vectivolt/PCM/docs/reference-designs/ti/tmdscncd28388d/README.md

# TMDSCNCD28388D - F28388D controlCARD (TI)
180-pin HSEC8 edge-card controlCARD carrying the TMS320F28388D: the controller our CTRL-C2000 board is built around (D-004).
- **Facts** (SPRUIL8B, May 2020; PCB rev B as of 29 May 2020): 180-pin HSEC8 connector (100-pin DIMM only via the separate TMDSADAP180TO100 adapter); default 25 MHz clock (cards MCU063B and later need C2000Ware >= 3.02, older cards use 20 MHz); on-board isolated XDS100v2 JTAG; micro-USB J3 is NOT isolated from board ground; SCI boot uses GPIO28/29.
- **Informs:** CTRL-C2000 connector/pin plan, clocking, boot and emulation arrangement (ECO-01/02).
- **Limitation:** evaluation card ("not intended to be a complete customer design"); compliance is the system designer's job. No other design in this library targets F28388D (they use F280039/F280039C, F28379D, F2803x), so reference firmware must be ported.
- **Missing (MANUAL):** schematic, BOM, layout, Gerbers and the pin-map PDFs. TI's tool page says "Hardware files can be found by downloading C2000Ware at boards\controlCARDs\TMDSCNCD28388D"; there is no separate hardware download. C2000Ware 26.02.00.00.LTS is offered only as installers (Windows .exe, Linux .run, macOS .app.zip, about 323-327 MB) from dr-download.ti.com/secure/, shown with a lock icon (TI login). Checked 2026-10-04; per the brief nothing was downloaded or run. By hand: install C2000Ware and copy the PDFs/BOM out of that folder into this directory, then add rows to SOURCES.csv.
