vectivolt/PCM/docs/requirements/ARCHITECTURE-COSTFIRST.md

# Cost-first architecture — PV-P75 / PV-P100/110 (specification for the board designers)

**Date:** 2026-10-04 · **Decision basis:** D-044, `COST-REVIEW.md` · **Scope:** REQUIREMENTS.md §2, §2b, §7 (SRC-1…5)
· **Costed parts list:** `gen/data/costfirst_bom.csv` (block level, generated by a scratch script; totals in §14)

**Honesty boundary.** Nothing here is built, bought or measured. Every number is *calculated* (from the frozen
designs in `sim/out/…`), *looked up* (a price row in `gen/data/prices.csv` or a data sheet in `docs/datasheets/`), or an
*estimate* whose basis is written next to it. Standard values (IEC 60664-1, IEC 62477-1, IEC 62109, CISPR 11) are the
transcriptions from memory already used in `sim/insulation.py` (D-032) and are **not verified against the standard
text**. 86 % of the money in §14 is a low-confidence estimate.

---

## 0. The architecture in one page

```
                    reinforced barrier B1 (the only one)
   PE-referenced / SELV  ║   DC side ("live"), everything referenced to BUS-
  ───────────────────────╫──────────────────────────────────────────────────────────────────────
   CAN (BMS/PCS)  ◄──────╫── CA-IS3062W ──┐
   RS-485         ◄──────╫── CA-IS3082W ──┤
   ENABLE / E-stop ──────╫── CA-IS3821L ──┼── F280039C (C2000, live) ── trip LATCH ── PWM gating ──► 12/16 NSI6651 channels
   STATUS out     ◄──────╫── CA-IS3821L ──┤        │  ADC / CMPSS              ▲          (functional insulation,
   3 fans (24 V)  ◄──────╫── fan buck  ◄──┤        │                           │           per-phase bias transformer)
   SELV 24 V      ◄──────╫── AUX-T1 SELV winding (reinforced)                  │
                         ║   AUX-T1 live winding 24 V ─► coils, 5 V, 3.3 V     │ OC / OV / OT / DESAT / RDY / WD / STOP
                         ║   flyback primary ◄── diode-OR of A+ and B+ terminal sides (starts at 200-220 V)
  ───────────────────────╫──────────────────────────────────────────────────────────────────────
                    basic barrier B2: DC side ↔ earthed heatsink / chassis / PE
```

- **Power stage unchanged:** 3 (4) interleaved two-level FSBB phases, 2 × SG2M040170HJ per switch, 32 kHz, NSI6651
  channel rev 6, inductor rev M1, control and MPPT as designed.
- **Controller on BUS-:** one F280039C (4.40 USD) on a small control board; dividers, shunts and TMR sensors without
  isolated amplifiers; **one reinforced barrier** (communication, enable/stop, status, fans, SELV supply).
- **Self-powered:** one 75 W flyback (AUX-HV topology) from both ports' terminal sides, starting at 200-220 V; a
  reinforced SELV winding feeds fans and communication; no cabinet 24 V.
- **Ports:** PV port = varistor network + **one contactor** (+ pole), no fuse, no precharge. Battery port = varistor
  network + **one aR fuse per pole** + one contactor + precharge relay/resistor. No clamp banks.
- **One hardware latch** (no dual channel) with OC, OV, OT, DESAT, gate-supply loss, watchdog and external stop.
- **Two boards:** power board (~1,615 parts) + control board (~236 parts) = **~1,850 parts** (PV-P75).
- **BOM at catalogue / 1 k prices: 966 USD (12.9 USD/kW)** for PV-P75, **1,177 USD** for PV-P100/110 — 65 % below
  today's 2,789 USD, but **21 % above the 800 USD budget**. Chinese-volume view (stated factors, §14): ~736 USD.
- **What closes the gap:** the frozen inductor (240 USD = 25 % of the BOM at an 80 USD estimate each) has to be
  re-opened for cost; nothing else of that size is left that does not cost safety (§14).

---

## 1. Block diagram and circuits with their reference potential

### 1.1 Power path

```
 PV array                                                                                Battery / DC bus
 A+_T ─┬─[K_A HFE82V]──── A+ ── A bank 3(4)×2×45 µF ──┐                ┌── B bank ── B+ ─[K_B HFE82V]─┬─[F_B+ 250 A aR]─┬─ B+_T
       │                                           ┌───┴───┐        ┌───┴───┐          └[K_PRE+220 Ω]─┘                 │
   varistor Y                                      │ leg A │──L1─── │ leg B │   (× 3 or 4 phases, 120°/90°)          varistor Y
   VAX, IMD, AUX tap                               └───┬───┘        └───┬───┘                                AUX tap, VBX
 A-_T ─┴──[RS_A 100 µΩ]────────────────────────── BUS- ─────────────────┴──────────[RS_B 100 µΩ]──[F_B- 250 A aR]─┴─ B-_T
                                 (BUS- = controller ground; heatsink, chassis, Y caps, MOV3, IMD → PE)
```

### 1.2 Circuits and reference potential

| circuit | board | reference | insulation to BUS- | insulation to PE | insulation to SELV |
|---|---|---|---|---|---|
| port banks, legs, dampers, bleeders, inductors | power | A+/B+/BUS-/switch nodes | functional | basic (B2) | reinforced (B1) |
| 12 (16) gate-drive islands (NSI6651 output side, bias secondary, clamps, booster, DESAT) | power | each device's Kelvin source (S1/S3: switch node; S2/S4: BUS-) | functional (driver, bias transformer) | basic (by distance on the board, B2) | reinforced |
| gate-bias primaries (SN6505B, 5 V), NSI6651 input side | power | BUS- | — | basic | reinforced |
| TMR inductor-current sensors (primary at the switch node, output at BUS-) | power | BUS- | functional (sensor) | — | reinforced |
| port dividers VA, VAX, VB, VBX; PE divider; IMD strings | power | BUS- (bottom), poles/PE (top) | functional (pole-pole) / basic (PE strings) | basic | reinforced |
| port shunts RS_A, RS_B + amplifier | power | BUS- | — (same node) | basic | reinforced |
| contactor and precharge-relay coils + drivers | power + chassis | BUS- (coil low side) | functional coil-contact (Hongfa 3 kV AC) | **basic coil-to-mounting** (open item R-04) | reinforced |
| aux flyback primary, live 24 V / 5 V / 3.3 V rails | power | BUS- | functional | basic | reinforced (AUX-T1) |
| MCU, ADC front end, comparators, latch, watchdog, debug header | control (live zone) | BUS- | — | basic (by distance, coated) | reinforced (B1) |
| CAN, RS-485, enable/stop input, status output, fan supply + PWM + tach, SELV 24 V / 5 V | control (SELV zone) + fans | SELV 0 V, tied to PE via 1 MΩ ‖ 4.7 nF (Y2); installer may bond it solid (PELV) | reinforced (B1) | — (SELV/PELV) | — |
| heatsink, chassis, fan frames' mounting, terminal covers | mechanics | PE | basic (B2) | — | — |

---

## 2. Insulation concept

Requirements are the rows of `sim/out/insulation/insulation_spec.json` (working voltage 1000 V DC, 1100 V at the OV
trip, switch-node recurring peak 1,273 V at 1000 V / 1,401 V at the trip, OVC II, PD2 inside the coated electronics
compartment, PD3 in the cooling-air path). The varistor network of `gen/port.py` rev 6 limits the terminals to
**Up,eff = 3.79 kV** pole-PE and pole-pole; where this credit is used it is marked "credit" (D-032: the credit is not
verified against the standard text).

### 2.1 The barriers that remain

| # | barrier | type | requirement (insulation_spec row) | part(s) that provide it |
|---|---|---|---|---|
| B1 | DC side ↔ SELV (communication, enable/stop, status, fans, SELV supply) | **reinforced** | "Reinforced HV-PELV, DC pole": 1000 V DC working (BUS- is a DC node; no switching swing across B1); impulse 8 kV (6 kV with credit); AC test 4400 V rms 60 s; creepage 10.0 mm PD2 on the PCB (6.4 mm under an IEC 60664-3 coating = PD1); clearance 8.0 / 9.2 / 10.4 mm at 2000 / 3000 / 4000 m (5.5 / 6.3 / 7.1 mm with credit) | AUX-T1 SELV winding (TIW-litz, potted, PD ≤ 10 pC at 2461 Vpk, 4400 V rms, 8 kV — the AUX-HV T1 rev M1 construction rules); CA-IS3062W (CAN), CA-IS3082W (RS-485), 3 × CA-IS3821L (2-ch digital isolators: enable/stop, status, fan speed, 3 tachs) — SOIC-16 WB, 8 mm package creepage → **conformal coating to PD1 over the B1 zone is mandatory** (as PA-08 required for the old isolators) or the 15 mm WW variants; a routed slot under every isolator; the SELV harness (fan leads UL1007 300 V) runs in its own channel ≥ 10 mm from live parts or in a sleeve (supplementary insulation) |
| B2 | DC side ↔ PE (heatsink, chassis, enclosure) | **basic** | "Basic HV-PE": DC pole: impulse 6 kV (4 kV credit), 2200 V rms, creepage 5.0 mm PD2 / 12.5 mm (group I) – 16 mm (IIIa) PD3, clearance 5.5 / 6.3 / 7.1 mm (3.0 / 3.5 / 3.9 mm credit); switch node additionally PD-free: extinction ≥ 1528 Vpk ≤ 10 pC at 1910 Vpk | AlN 1.0 mm device insulators with 6.5 mm overhang (cell_spec `heatsink_insulator`, unchanged); inductor winding-core-mounting (rev M1 insulation system); contactor and fuse bodies (maker ratings); terminal feed-throughs (PD3 creepage); Y1 capacitors (8 kV); MOV3 of each varistor Y; IMD strings (8 × 1210, 1000 V each); heatsink NTC probes (≥ 2.2 kV rms lead-to-lug, R-10); insulating PCB standoffs; **contactor coil-to-mounting** (new: the coil is live now — Hongfa states coil-contact 3 kV AC only, R-04) |
| B3 | inside the DC side | functional | withstand 1000 V DC + 1,401 V recurring peak + 3.79 kV pole-pole surge; **our rule:** PD-free at ≥ 1.75 kVpk (1.25 × the recurring peak) for everything that sees a switch node | NSI6651 (reinforced part, VIORM 2121 Vpk, used functionally), per-phase bias transformer (custom, §4), TMR sensors, dividers, contactor coil-contact (3 kV AC), CA-IS3417WT (IMD), CNY65B (varistor monitor), AUX-T1 primary ↔ live winding |

**What disappears:** the 132 audited HV-PELV barriers of the old platform (12 UCC14241, 12 NSI6651 as safety
barriers, AMC3330/AMC3302, TPSI3050, contactor coils, CNY65B, AUX-HV T1, LA 150-P …) become functional; the 22
barrier failures at 2000 m that came from HV-PELV parts (IC-02/03 surge ratings of AMC3302 / UCC12050, IC-04 precharge
relay, IC-05 contactor coil) no longer apply; the B2 items among them (heatsink pads, magnetics insulation, X-capacitor
specs) stay open as before. Six parts carry the safety barrier B1 (AUX-T1 and five isolators).

### 2.2 The hard questions

- **Fans.** They cannot be live: the fan's own dielectric rating is **500 V AC 1 min frame to + lead** and the leads
  are UL1007 300 V (Delta AFB1224SHE-F00 spec p.2, `docs/datasheets/thermal/AFB1224SHE-F00.pdf`), against 2200 V rms
  needed for basic insulation of a 1000 V DC circuit. The fans are therefore on the SELV side: powered from the
  reinforced SELV winding of AUX-T1 through a 7-24 V fan buck on the control board, speed command and tachs across
  B1 (isolator channels). Fan frames are plastic (UL94V-0) and mounted on the earthed chassis; the fan's internal
  insulation is only functional, which is acceptable for an SELV circuit.
- **Communication ports.** CAN and RS-485 transceivers are isolated (reinforced, B1); their bus sides, the
  terminations, TVS (SM712-class to SELV 0 V, SMBJ to PE) and the connectors sit in the SELV zone at the front panel.
  The BMS / PCS side may earth its 0 V; the SELV 0 V is tied to PE through 1 MΩ ‖ 4.7 nF Y2 so a solid bond by the
  installer (PELV) is harmless.
- **Enable / emergency-stop input.** A dry contact (or 24 V SELV signal) in the SELV zone drives a reverse isolator
  channel of the **default-low** variant: SELV supply lost, wire broken or contact open = STOP. The isolator output
  sets the hardware latch (§6) directly — firmware is not in the path. It is a single-channel functional stop, not a
  SIL/PL-rated safety function (§12).
- **Service / debug connector.** The JTAG/cJTAG header is on the **live** zone, inside the enclosure only, marked
  "HAZARDOUS VOLTAGE — isolated debug probe only (≥ 1000 V DC rated, e.g. an isolated XDS)". Field service and
  firmware update go over CAN (SELV) with a CAN bootloader: no live access is needed in the field. This is the
  normal arrangement for this product class (COST-REVIEW §4).
- **Heatsink.** **Earthed (PE)**, as D-032 froze it. The alternative — heatsink on BUS- — would cut the common-mode
  source (the switch-node tabs see the heatsink through ~24 pF each) and allow thinner functional pads, but it puts a
  large live metal part in the PD3 air path (16 mm creepage standoffs, IPXXB at both air openings) and is a trap for
  service staff who expect an earthed heatsink. Rejected on safety; the EMI cost of the earthed heatsink is one
  nanocrystalline core per port (§8).
- **What the earthed enclosure must provide.** (1) A PE stud with ≥ 16 mm² Cu (line conductors 35-50 mm²; the stud carries the installation's PE sized to the line
  conductors - the module's own PE bond is ≥ 10 mm² Cu per D-048, INSTALLATION.md INST-42) and the
  heatsink bonded to it at two points (≥ 6 mm² each); (2) IP20 / IPXXB for every live part with the covers closed,
  covers removable only with a tool; (3) the label "Hazardous voltage — wait 10 min (PV-P100/110: 15 min) after
  disconnection" (passive bleeders, §8); (4) DC terminals at the rear with touch covers and PD3 creepage ≥ 16 mm;
  SELV connectors at the front, ≥ 10 mm from any live part; (5) the cooling-air path separated from the coated PD2
  electronics compartment (D-032); (6) the PE return for the Y capacitors, MOV3 and the IMD strings (removable strap
  for the hipot, as port.py's PE_T).

---

## 3. Auxiliary supply

**Topology:** single-switch DCM flyback, the AUX-HV rev C1 circuit (`gen/aux_hv.py`): UCC28C59-Q1 at 64.9 kHz, 48 %
duty limit, one 1700 V SiC switch (IV2Q171R0D7Z / SG2M1K0170J2J), BSS126 cascode start-up, TPS3710 brown-in,
TLV3202 input-OV lockout + overload timer, TVS clamp. **Changes:** rating 30 W → **75 W continuous** (new transformer
AUX-T1, EC41/ETD39 class; first estimate Lp ≈ 0.7 mH, Ipk ≈ 2.0 A at 200 V, to be designed with
`sim/aux_hv_design.py` and `sim/magnetics.py`); the primary and the controller are referenced to BUS-, so the live
24 V winding is regulated **directly** (divider into the UCC28C59 FB pin — no optocoupler, no TL431); the second secondary is the
reinforced SELV winding.

**Input:** one tap per port on the terminal side (before K_A / K_B): 2 × 22 Ω pulse-rated wirewound + 1 A 1000 V DC
fuse + 1600 V diode each (the AUX-HV input block), diode-OR, 2 × 3.3 µF 1300 V film surge absorber. A reversed port
is blocked by its diode. Brown-in 220 V rising / 200 V falling → the module wakes at ≤ 250 V on either port (PV-C2).

| output | where | load (PV-P75) | load (PV-P100/110) |
|---|---|---|---|
| live 24 V (BUS-) | contactor coils: pull-in 6 W each for 0.1 s, one at a time, then PWM economiser ~1.5 W each | 3.0 W | 3.0 W |
| live 24 V → 5 V buck | gate-drive bias: 12 (16) × 0.42 W (0.273 W gate charge at 32 kHz + VCC2 quiescent + regulation) / 0.85 / 0.90 | 6.6 W | 8.8 W |
| live 5 V / 3.3 V | NSI6651 input sides, F280039C, logic, comparators, op amps, 3 (4) TMR sensors | 1.4 W | 1.5 W |
| live 24 V | precharge relay coil (≤ 5 s per start) | (2 W) | (2 W) |
| **SELV 24 V** (reinforced) | 3 fans: AFB1224SHE 12 W each at full speed (PV-P100/110: FFB1224SHE capped at 17 W each) + 10 % buck loss | 39.6 W | 56.1 W |
| SELV 5 V | isolator SELV sides, CAN/RS-485 transceivers, enable/status | 0.6 W | 0.6 W |
| **total output, fans at full speed** | | **51 W** | **70 W** |
| typical at full power, 45 °C inlet (fans ≈ 72 %, power ∝ speed³) | | ≈ 26 W | ≈ 34 W |
| **standby** (contactors held, gates off, fans off): aux ≈ 9 W input + bleeders 2.5 W + dividers 1.0 W + varistor monitor loops 2.2 W | | **≈ 15 W** | ≈ 16 W |

Megarevo publishes standby < 20 W: met by estimate. **Start-up:** 3.0 s typical / 6.2 s worst after brown-in
(AUX-HV figure). **Hold-up:** 2 × 1000 µF / 35 V on the live 24 V give ≥ 40 ms at 11 W (24 → 8 V) for a controlled
stop; the contactors drop ~50 ms after a total loss of both port voltages (see §6.4 for the residual risk).

---

## 4. Gate-drive bias for 12 (16) channels — functional insulation only

Bootstrap is impossible: in buck mode S3 stays on, in boost mode S1 stays on (cell_spec `switching.modes`).

| scheme | parts / channel | cost per channel | barrier C (pri-sec) | CM current at 124 V/ns* | regulation of +18 / −3.5 V | supply-loss detection | risk |
|---|---|---|---|---|---|---|---|
| (a) TI UCC14241-Q1 per channel (today) | ~15 | 4.97 USD (TI 1 ku) + 0.6 | < 3.5 pF | ≤ 0.43 A | ±1-2 %, regulated | PG → RDY | proven; 12 × 5.6 = 67 USD; reinforced rating now unused |
| (b) Mornsun QA243C / QA243CT per channel | ~4 | ~4 USD (not verified, D-036) | 3-5 pF | ≤ 0.62 A | unregulated, ±15 % | none (driver UVLO) | **no +18/−3.5 V model** (only +18/−3 V: die margin vs 1.94 V threshold falls from 0.56 V to ~0.06 V) — rejected |
| **(c) one transformer per phase, SN6505B push-pull, 4 secondaries, per-channel LDO + shunt split (chosen)** | ~11 + 5 per phase | **0.98 USD** (0.30 + (0.93 + 1.80) / 4) | ≤ 5 pF specified (sectioned bobbin, TIW) | ≤ 0.62 A | LM317L-class LDO to 21.5 V ±2 %, TL431-class shunt holds COM−VEE at 3.5 V ±1.5 % | NSI6651 VCC2 UVLO → RDY (wired-AND) → latch; 5 V primary supervised | custom magnetic (MAG-1/2); PD-free design at ≥ 1.75 kVpk between secondaries |
| (d) gate windings on the main flyback | ~10 | ~0.5 USD | 10-30 pF (large transformer) | > 1 A | cross-regulation with the 4:1 input range | UVLO | 14-18 windings on one part, poor regulation, one failure takes all channels — rejected |

\* Worst turn-on dv/dt 124 V/ns (cell_spec report §4). In the new architecture this current flows from the switch
node through the barrier capacitance **back to BUS- locally** (the controller ground is BUS-), instead of into the
earthed PELV ground as before; it is a layout matter (bias primary and driver input side close together, decoupled to
BUS-), not a safety matter.

**Choice (c):** per phase one SN6505B (5 V, 420 kHz) + one custom EP10-class transformer (centre-tapped primary,
four TIW secondaries, ratio ≈ 1:5.2 → ≈ 26 V raw); per channel a 4 × 1N4148WS bridge, an LM317L-class LDO set to
21.5 V (VDD−VEE) and a TL431-class shunt that holds COM−VEE at 3.5 V; the rev-6 channel's 3 × 22 µF stay. Cost
11.8 USD for 3 phases (15.7 for 4) against 67 USD (89 USD) with UCC14241. What changes in `gen/gdrv.py`: a new
option `bias="ext"` in `channel()` that omits the UCC14241 block and its PG FET and takes VDD/COM/VEE from the
caller; everything else in the channel (clamps, booster, DESAT string, interlock stretcher) is reused unchanged.

---

## 5. Sensing without isolated amplifiers

Accuracy targets: Megarevo publishes voltage and current accuracy < 1 % at 100 % Pn; `control_spec.json
measurement_requirements` sets the rest.

| quantity | how | part(s) | accuracy (after end-of-line 2-point calibration) | bandwidth / delay | dv/dt exposure |
|---|---|---|---|---|---|
| VA, VB (bank side) | 6 × 1 MΩ 0.1 % 25 ppm/K 1206 + bottom R into a buffer, RC pole 5.8 kHz (as designed) | Viking ARHV06BTC1004A | ≤ 0.5 % (TCR mismatch 0.15 % + ADC/reference 0.3 %) | 5.8 kHz; OV path ≤ 35 µs (required ≤ 58.5 µs) | none (DC node, 96 kHz ripple < 1 V) |
| VAX, VBX (terminal side, before the contactor) | same divider, bipolar range (offset to mid-scale) → polarity, precharge ΔV, weld check | same | ≤ 0.5 % | 1 kHz | none |
| port currents IA, IB (needed: CPL feed-forward at 250 V, MPPT power, < 1 % reporting, contactor hold-off) | **shunt in BUS- of each port** (2 × 200 µΩ metal strip in parallel), zero-drift difference amplifier on BUS-; second gain path for the ±1.5 kA hold-off comparator | 3920 metal strip + SGM8552-class | ≤ 0.8 % at 135 A (shunt TCR compensated with the board NTC) | ≥ 10 kHz, ≈ 2 µs | none: the shunt's common mode is 0 V (it sits on the controller ground) |
| inductor current, per phase | open-loop TMR sensor with PCB primary, 5 V, ±100 A of ±325 A | Sinomags STK-HO/A 130 (alt. CHIPSENSE) | ±1.5 % (±3 % over temperature, data sheet) → gain/offset trimmed, offset re-zeroed at every idle (as control_spec plausibility rules); sharing needs ±2 % | 1 MHz, 0.2 µs (required ≥ 200 kHz, ≤ 4.14 µs group delay) | **yes: primary at a switch node, 124 V/ns** — no maker figure for dv/dt immunity (R-07); trip comparator with 100 ns RC |
| heatsink temperature (1 per phase section) | NTC 10 k lug probe on the earthed heatsink, **≥ 2.2 kV rms lead-to-lug** (it bridges live control and PE) | EXSENSE / Shiheng class | ±2 K | thermal | none |
| inductor temperature | NTC in the rev-M1 winding pocket (functional to the winding) | same | ±2 K | thermal | via the pocket only |
| inlet air | NTC on the control board | same | ±1 K | thermal | none |
| insulation resistance (PV-C5) | divider PE → BUS- (bipolar) + VAX (array side, K_A open); two switched 992 kΩ strings, A+ → PE and PE → BUS-, each through an isolated 1700 V SiC SSR; two-state method of `sim/port_design.py` §8 with the 3-sample exponential prediction | 2 × CA-IS3417WT, 16 × ARHV13 124 k | 33 kΩ: ~10 %, 1 MΩ: ~2-5 % (old design's figures, same method) | 3 s per result | none |

> *Correction 2026-10-05:* PV-PWR draws the Sinomags **STK-HO/A 75** for the inductor current, not the STK-HO/A 130 named in the table. Reason (PV-PWR design check): after the 2-point calibration and the idle re-zero, the 75 A part gives 1.8 % sharing error at 45 A against the ±2 % needed; the 130 A part gives 2.8 %. Its linear range of ±187.5 A covers the 100 A measuring range and the backup-trip peak. Since PV-PWR rev A2, each sensor's reference output also goes to PV-CTL, which sets its hardware trip window from it.

What makes this cheap: every sensor output is referenced to BUS- = the ADC ground. The only signals that cross a
switch-node potential are the 3 (4) TMR sensors, and they carry their own magnetic separation.

---

## 6. Protection and safety concept

### 6.1 Trip sources → one latch

| source | detection | threshold | path (no firmware) | gates off after the event |
|---|---|---|---|---|
| inductor over-current, per phase | TMR → window comparator | ±72.2 A (band 68.5-76 A) | comparator → latch → AND gates on all PWM lines + all drivers' EN | ≤ 1.5 µs (TMR 0.2-0.3 µs + comparator 0.3 µs + logic + NSI6651 90 ns + gate fall); required ≤ 8.9 µs (control_spec local layer) |
| inductor over-current, backup | F280039C CMPSS (one per phase, H + L) → ePWM trip zone | ±92 A (84-98.6 A) | on-chip, configured at boot | ≤ 1.3 µs; required ≤ 4.87 µs |
| short circuit / shoot-through | NSI6651 DESAT (9.26 V, 465 ns blanking) + rev-6 booster | per channel | driver soft turn-off; FLT_N (wired-OR) → latch → all other channels | 0.62 µs (frozen channel) |
| port over-voltage A and B | bank-side divider → comparator | 1100 V (software limit 1050 V) | → latch | ≤ 35 µs (required ≤ 58.5 µs) |
| over-temperature | heatsink NTCs → comparator; inductor NTCs → comparator | heatsink 95 °C; inductor 145 °C (10 K below the 155 °C hot-spot limit) | → latch | thermal |
| gate-drive supply lost | NSI6651 RDY (UVLO either side, wired-AND); 5 V / 24 V supervisor | UVLO | → latch | ≤ 1 µs |
| watchdog | 74LVC1G123 heartbeat monoflop (ISR toggles a pin; 5 ms) + TPS3823 reset (1.6 s) | 5 ms | → latch | 5 ms |
| external stop | SELV contact → default-low isolator channel | open contact / lost SELV supply | → latch | ≤ 2 ms (debounce) |
| reverse polarity / precharge | VAX, VBX comparators | VBX < +200 V, ΔV > 10 V | blocks the contactor coil drivers (hardware AND) | — |

**The latch:** one set-dominant flip-flop (74LVC1G74) with a diode/gate OR of all sources. Output: (1) AND gates
(3-4 × 74LVC08) on every PWM line, (2) all NSI6651 RST/EN low (latches their fault state, ≥ 0.8 µs), (3) the MCU trip
zone (INPUT X-BAR) and a GPIO, (4) the contactor logic (§6.2), (5) the status output. It can be cleared only by a
firmware pulse **and** only while no source is active. No dual channel, no fault analysis (D-044).

### 6.2 Contactor rules (K_A, K_B, K_PRE)

1. **Close** only with the latch clear, the terminal voltage of the right polarity (VAX/VBX > +200 V — hardware
   interlock in the coil driver, so firmware cannot close onto a reversed source), the IMD result ≥ 33 kΩ before K_A
   (IEC 62109-2 V/30 mA rule — from memory) and |V_bank − V_terminal| ≤ 10 V for K_B (after precharge, the
   `port_spec` criterion). K_A closes after the converter has pre-charged the A bank from port B (ΔV ≤ 20 V) when
   the battery is present; on a PV-only start it closes onto the empty bank, limited by the array (≤ 169 A) — the
   making current (Isc plus the discharge of the array/cable capacitance, ~0.5 kA estimate) must be confirmed with
   Hongfa (R-04).
2. **Open** for a normal stop only after the converter has stopped and |I| < 300 A has held for ≥ 20 ms (two release
   times): HFE82V-300C/1000 is rated for 200 openings at 300 A / 1000 V.
3. **Fault opening up to 1.0 kA:** the hardware hold-off keeps the coil energised while |I_port| ≥ 1.0 kA (band
   0.95-1.05 kA: shunt 1 % + comparator + reference). The hold can only keep an energised coil on; it can never
   energise an open contactor. The contactor's one-time breaking capacity is 1500 A at 1000 V ("no fire, no
   explosion", HFE82V data sheet), so 1.05 kA keeps a 1.4× margin. Every opening above 300 A flags the contactor for
   replacement.
4. **No auxiliary contact** (HFE82V has none): a weld is found by moving the bank voltage ≥ 50 V after opening and
   checking that VAX/VBX does not follow; a weld blocks restart.

### 6.3 Battery port coordination and the installation requirement

| current fed from the battery into the module | who clears it |
|---|---|
| ≤ 300 A | converter control / K_B (normal) |
| 300 A – 0.95 kA | K_B opens (fault opening, contactor replaced afterwards) |
| **0.95 kA – 1.3 kA** | **neither guaranteed in the module** — K_B holds, the HPE501 250 A aR fuse may melt but is rated to break only from 5 In = 1.25 kA (+10 % curve tolerance) |
| 1.25 kA – 50 kA | HPE501/000B100-250 per pole (aR, 1000 V DC, L/R 1-3 ms; clearing I²t ≤ 85 kA²s) |

**Installation requirement (battery / DC-bus side), stated as numbers:**
- The upstream battery protection (rack fuse, DC breaker or BMS-controlled rack contactor) must interrupt **any
  current between 0.95 kA and 1.3 kA flowing into the module's battery port within 0.25 s** (the drawn port_spec /
  port report states 0.97-1.25 kA within 0.26 s at L/R ≤ 1 ms; the stricter of each pair - 0.95-1.3 kA, 0.25 s - satisfies both
  and INSTALLATION.md carries the drawn values; the HPE501 250 A
  pre-arc time at 1.375 kA, i.e. 1.25 kA + 10 % tolerance, read from its curve; the contactor carries 1000 A for 25 s).
- The prospective short-circuit current at the module's battery terminals must not exceed **50 kA with L/R ≤ 3 ms**.
- The cable from the battery protection to the module is protected by that upstream device (the module fuses protect
  the module, not the external cable).
- One active insulation monitor per galvanically connected system: PV array and battery are one system through
  BUS- (§5, port.py rule kept).

**PV side:** array Isc at the module terminals ≤ 1.25 × 135 A = 169 A (225 A for PV-P100/110); string fuses in the
combiner per IEC 62548; a load-break DC isolator upstream for maintenance; the array floating (IT) or one pole earthed
in agreement with the IMD.

### 6.4 Reverse polarity, terminal shorts, residual risks

- **Reverse polarity (both ports, no clamp diodes):** the + pole contactor stays open, the aux tap's diode blocks, the
  varistor pairs (2 × V1mA 750 V) do not conduct at 1000 V, so no current flows; VAX/VBX read negative → alarm.
  Firmware cannot close onto it (hardware interlock 6.2-1).
- **Bolted short at a port's terminals (no clamp banks):** the bank (270 µF, 135 J at 1000 V) dumps through the
  contactor (≈ 22 kA peak, weld likely) and rings below zero; the leg body diodes carry up to ≈ 4.5 kA per device
  (`report.md` §7) → **the port-side legs are likely destroyed**. On the battery port the dump (≈ 39 kA²s) also melts
  the aR fuses (pre-arc 5.3 kA²s); the battery's own current flows in the external short, outside the module, and is
  the upstream protection's job; the PV array keeps feeding an external PV short (current-limited, the installation's
  matter). The module then stays latched and is repaired. It is not expected to burn: a PV-fed internal short is
  opened by K_A (≤ 169 A ≪ 1.0 kA); a battery-fed one by the fuses.
- **Residual:** total loss of both port voltages (hence of the aux supply) while > 1 kA flows → the contactor opens
  above its rating. This needs a bolted terminal short (then I ≫ 1.25 kA and the fuse clears in < 10 ms, before the
  contactor releases in ~50 ms) — the same class of residual as D-033's "double fault".

---

### 6.5 Hardware / firmware allocation (owner instructions 2026-10-04 / 05, decision D-050)

The owner: "don't try to handle everything in the hardware … offload whatever possible to the firmware to save cost …
a sweet balance between hardware and software for edge cases", then: "but if it's not a significant saving, keep it",
then: "decide yourself everything".

**Decision: the hardware protections of §6.1 stay.** Moving them into the controller was worked out part by part and
would save about 17 USD per module (control board about 5, the two ports about 11, the dead-time stretch about 1.5)
— roughly 2 % of the bill of materials — and what it gives up is not worth that:

| Protection | Cost of keeping it | Why it stays |
|---|---|---|
| Discrete per-phase over-current comparators, port over-voltage comparators, over-temperature comparators, the one latch, the gating on the PWM lines, heartbeat watchdog (control board) | about 5 USD | An independent layer that works with the controller mis-programmed; the controller's own comparators remain the backup |
| RC dead-time stretch per gate-drive channel | about 1.5 USD | With it removed, a firmware dead time of zero gives about 85 ns of overlap per edge (about 59 mJ) that ends before the driver's DESAT blanking: nothing catches it and the switches fail within milliseconds (`gen/gdrv.py` rev 9) |
| Negative-rail detector per channel | about 0.03 USD per channel | A lost negative rail gives +5.1 V at the die, 1.57 mJ per event, about 50 W at 32 kHz — survivable but never seen by DESAT |
| Polarity and precharge ΔV interlocks in the coil drivers, port over-current comparators (power board) | about 11 USD for both ports | A firmware error here closes a contactor onto reversed polarity or a large voltage difference, or lets a battery-fed fault melt a fuse link below its breaking range: destroyed devices or a welded contactor |
| Contactor hold-off comparator, external stop onto the latch, DESAT, driver under-voltage lock-out, default-off pull-downs | — | Must work with the controller dead; a hazard otherwise |

**Where the rule does apply:** no new hardware is added for a rare edge case unless firmware demonstrably cannot
cover it; sequencing, monitoring, plausibility checks, temperature-dependent limits, the insulation monitor's
algorithm, fan control and every "what if" that is not a hazard are firmware. Firmware also duplicates each hardware
trip as a second layer (thresholds, timing, a start-up self-test of each trip path) — listed in
`sim/out/port_design/port_spec.json` (`lean.firmware_requirements`), the control board's design check and
`sim/out/pv_control/control_spec.json`. The lean-port functions and the gate-drive channel keep the lighter
variants as options (`interlocks="hold"`, `oc_trip=False`, `stretch=False`, `neg_det=False`) should a later cost
round want them.

---

## 7. Controller: TI F280039C

**F280039CSPZR (100-LQFP): 4.395 USD at 1 ku** (TI.com product page, read 2026-10-04; row appended to
`prices.csv`; 64-pin 4.195, 80-pin 4.295). Data sheet SPRSP61C saved as `docs/datasheets/controllers/TMS320F28003x.pdf`.

| resource | F280039C (100-pin) | PV-P75 needs | PV-P100/110 needs | verdict |
|---|---|---|---|---|
| ePWM channels | 16 (8 modules, 8 with HRPWM) | 12 (2 modules per phase: leg A, leg B, on one carrier per phase, 120° shift) | **16 — all of them** | fits; fan speed then from an eCAP in APWM mode (3 eCAPs) |
| ADC | 3 × 12-bit, 4 MSPS, 25 channels | 3 i_L + 2 I_port + 4 V_port + 1 PE + 7 NTC + 2 rails = **19** | 4 + 2 + 4 + 1 + 9 + 2 = **22** | fits (80-pin package has 18: not enough) |
| ADC timing | 250 ns per conversion per ADC | per phase 2 SOCs per 31.25 µs period (carrier zero and peak + 0.87 µs lag compensation) = 6 (8) SOCs; VA/VB every ≤ 10 µs for the OV post-processing block; NTCs slow | | < 5 % of the ADC capacity |
| CMPSS | 4 (2 comparators + 2 DACs each) | 3 bidirectional i_L backups | **4 — all** | port OV / short stays external (§6.1) and in the ADC PPB |
| CPU / CLA | 120 MHz C28x + 120 MHz CLA, FPU, TMU | current loops at 64 kHz (double update): ≈ 200 cycles each → 3 × 2 × 200 / 120 MHz = 10 µs per 31.25 µs on the CLA (32 %) | 13.3 µs (43 %) | sufficient, but the old ISR budget (14.2 µs, F28388D at 200 MHz) must be re-timed — R-14 |
| communication | 1 DCAN + 1 MCAN, 2 SCI + 2 LIN-UART, 2 SPI, 2 I2C | CAN (BMS/PCS), RS-485 (SCI), EEPROM (I2C) | same | fits, one CAN spare |
| GPIO | 51 | PWM 12 + trip/latch/FLT/RDY 6 + coils 3 + IMD 2 + fan PWM/tach 4 + status/enable 2 + CAN 2 + SCI 2 + I2C 2 + WD 1 + latch clear 1 + bias enable 1 + LED 2 = **40** | 44 | fits (100-pin needed) |
| watchdog | windowed WD on chip | + external heartbeat (§6.1) | | ok |

The pin-level plan is the control-board designer's job; nothing above needs more than one F280039C.

---

## 8. Port and EMI filter

**Kept from `gen/port.py` rev 6, unchanged:** the monitored varistor Y per port (3 × Thinking TVT25751, two ETI
CH14×51 36 A branch fuses in PCB clips, one CNY65B monitor loop, 12 × 82.5 k), Up,eff 3.79 kV; the X capacitor at the
network (2.2 µF / 1300 V, impulse ≥ 4.5 kV, PA-07); 2 × 4.7 nF Y1 per port; the divider strings; the precharge sizing
method (`sim/port_design.py` §1) and the IMD equations (§8).
**Gone:** NH fuse bases and gPV/gBat NH links, the second (parallel) battery contactor, the TDK HVC43 contactors, the
active discharge with Miba resistors and thermostats, the 2oo2 hold-closed interlock, proof-test readbacks, the
AMC3330/AMC3302 channels, the TPSI3050 + 6 × C2M1000170D IMD switches, the 160 A custom CM chokes, the shunt busbars.
**New:** HFE82V contactors with live coils, HPE501 aR fuses (battery port only), BUS- shunts, CA-IS3417WT IMD
switches, passive bleeders (800 kΩ per port: 60 V after 10 min, 13.5 min for 360 µF; label), one nanocrystalline
ring core per port.

### 8.1 Common-mode filter re-derived for 150 kHz – 30 MHz

**Source:** the switch-node device tabs (S2 drain = node A, S4 drain = node B) face the earthed heatsink through the
AlN pad: 24 pF per device (AlN εr 8.8, 3.1 cm², 1 mm), 58 pF per switching node with the board and inductor (10 pF
assumed). Node swing 1000 V, 124 V/ns. **Calculated** (scratch FFT, three phases at 120°, Y caps 2 × 9.4 nF, 150 Ω CM
network, no choke): worst single harmonic **106-112 dBµV** at 150-300 kHz (duty-dependent; interleaving cancels the
non-triple harmonics), ≤ 93 dBµV from 0.5 to 30 MHz.

**Limit:** the DC power port of class A group 1 equipment in CISPR 11 (GCPC, 20-75 kVA row), *from memory, verify*:
QP 116 → 106 dBµV and AV 106 → 96 dBµV (0.15-0.5 MHz), QP 106 / AV 96 dBµV above. Against the AV line (~103 dBµV at
288 kHz) the estimate is up to ~10 dB over → **requirement: ≥ 16 dB of CM attenuation at 150-500 kHz (10 dB + 6 dB
margin), ≥ 6 dB above 0.5 MHz.** Solution: one nanocrystalline ring (~63 × 38 × 25 mm) around both conductors of each
port, single turn, |Z| ≥ 100 Ω from 150 kHz to 30 MHz, plus the existing Y caps; footprint and space for a second core
or a 2-turn version. If the ≤ 20 kVA row (AV 84 → 76 dBµV) were imposed, ~30 dB would be needed: a wound 2-3 turn CM
choke per port (+20-30 USD) — decide with the first pre-compliance scan.

**Leakage-current limit (stated):** the module's common-mode current below 150 kHz into PE / the PV array
capacitance ≤ **30 mA rms** (10 % of the 300 mA continuous residual-current threshold of IEC 62109-2 for
transformerless PCE, so a PCS RCMU never sees the DC/DC); touch current with PE open ≤ 3.5 mA (IEC 60990 weighting).
Estimate without any choke: **0.5-16 mA rms** (three phases interleaved, duty-dependent) → met. The old requirement
(L_cm ≥ 0.5 mH at 10 kHz, |Z| ≥ 50 Ω at 16-100 kHz) was self-imposed and is dropped.

### 8.2 PV port: contactor yes, fuse no, precharge no

One HFE82V-300C/1000 in A+, because (1) it is the reverse-polarity protection (no series diode, no clamp, no loss);
(2) a PV array is a current source that no upstream device will clear: a module with a failed-short leg would be fed
up to 169 A indefinitely — the contactor isolates it (169 A ≪ 300 A); (3) it disconnects the array for the IMD
measurement and controlled stops. Cost 55.7 USD with its driver. No fuse: the array cannot exceed 169 A (below any
fuse's fusing current, `port_design` §6.5); reverse current from the module into an array fault is limited by the
converter (S1 body diode path needs S3 on → OC trip). No precharge: the array is current-limited; when the battery is
present the converter pre-charges the A bank first.

---

## 9. Thermal

**Losses** (cell_spec / report.md §2, 45 °C inlet, full power): devices 178.7 W per phase at 611 → 611 V (worst),
**536 W (3 phases) / 715 W (4)**; inductors up to 51 W each (154 / 205 W), in the air stream downstream of the
heatsink; port parts ≈ 65 W (2 aR fuses 22 W each at 135 A, contactors 2 × 3.6 W, shunts 2 × 1.8 W, busbars ~10 W);
aux ≈ 10 W.

**One heatsink** for all 24 (32) devices (two rows: leg-A devices, leg-B devices), earthed, AlN pads and clips as
frozen. Target **R_sa ≤ 0.06 K/W at 400 m³/h** (including the air rise) → T_sink ≤ 80 °C and **Tj ≤ 110 °C** at
45 °C inlet and full power (ΔT_j-sink = 45 W × (0.39 + 0.198 + 0.08) K/W = 30 K). The old per-cell heatsinks had
0.045 K/W *each* (Tj 78 °C) — 3.7 times the aluminium that is needed; one ~3.6 kg extrusion (21 USD) replaces 3 × 4.4 kg
(81 USD). Margin given up: Tj 78 → ~110 °C at 45 °C; R_DS(on) +12 % (assumption) costs ≈ 42 W at full load
(−0.05 % points); at 60 °C inlet Tj reaches the 125 °C design limit at full power, i.e. derating starts near 55 °C
(PV-20 allows it above 45 °C). Heatsink trip stays 95 °C. Module efficiency (estimate): the +42 W of hotter devices
is roughly offset by losses removed elsewhere (two NH links on the PV port ≈ 28 W, the CM-choke windings ≈ 15 W), so
the published 99.49 % peak and the ≥ 99 % requirement (PV-11) should hold. **To be re-run** in `sim/pv_module.py`
with the new geometry, fans and port parts.

**Fans:** 3 × **Delta AFB1224SHE-F00** (Taiwanese maker, data sheet on file): 24 V, 12 W (max 18 W), 258 m³/h free
air, 142 Pa, 53 dB(A) — **12.85 USD @504** (Master Electronics, web-search result) against 88-113 USD for the Sanyo
9GT. Operating point ≈ 150 m³/h at 60 Pa each (linear estimate between the published free-air and shut-off points;
requires heatsink + module ≤ 60 Pa at 140 m³/h per fan section — a rule for the mechanical design). Noise: 3 × 53 dB(A)
+ 3 dB installation ≈ 61 dB(A) ≤ 65. Air rise ≈ 6 K. Speed control by supply voltage (7-24 V fan buck) because the
-F00 variant has no PWM input; tach per fan across B1. **Gap:** rated −10…+60 °C against PV-20's −30 °C: order the
low-temperature grease option or apply a firmware rule (fans held off below −10 °C inlet, power limited to the
fan-less capability until the inlet warms) — R-05. No backflow shutters: with one shared heatsink a dead fan's
section is still cooled by its neighbours (to be confirmed in the thermal re-run).

**PV-P100/110:** 4 × 120 mm fans do not fit the 444 mm width (480 mm); use 3 × FFB1224SHE-F00 (19.2 W, 290 m³/h,
capped at 17 W by the aux budget) on a 4.8 kg heatsink with R_sa ≤ 0.049 K/W. The old model already derated PV-P100/110
from 40 °C; this variant needs its own thermal run (R-17).

---

## 10. Board split, connectors, part counts

**Two boards, not one.** The power board is a large 6-layer heavy-copper (≥ 3 oz) board carrying 135-180 A;
putting the 100-LQFP MCU, the ADC front ends and the SELV zone on it costs ~3× per cm² compared with a 4-layer 1 oz
board, keeps the analog front end 30-50 mm closer to 124 V/ns nodes, and prevents testing (and hipot-testing B1) as a
sub-assembly. The control board is also the one board the DAB can reuse (§16). Cost of the split: one connector pair
(0.90 USD) and one small PCB.

| board | contents | parts (PV-P75) | parts (PV-P100/110) |
|---|---|---|---|
| **POWER** | 24 SiC, 12 port film + 18 decoupling, dampers (48), bleeders (16); 12 gate-drive channels (~85 each = 1,020) + bias (3 × SN6505B + transformer, 12 regulators ≈ 147); 3 TMR sensors; BUS- shunts + amplifier; 5 dividers (40); IMD (22); 2 varistor networks with X/Y caps (50); 3 coil drivers (25); aux flyback (~145); press-fit terminals and connectors (23) | **~1,615** | ~2,050 |
| **CONTROL** | live zone: F280039C + crystal + EEPROM + supervisor/heartbeat, latch + PWM gating, trip comparators, ADC front end, debug header (~180); SELV zone: 5 isolators, CAN/RS-485 protection and connectors, enable/status, fan buck and 3 fan headers (~56) | **~236** | ~240 |
| chassis | 3 (4) inductors, 2 contactors, 2 aR fuses, precharge resistor, 4 terminals, busbars, 3 fans, heatsink + NTC probes | (in the BOM, not placements) | |
| **module** | | **~1,850** (target 1,000; today 3,345) | **~2,290** |

The ~1,000-part target is **not reachable with the frozen gate-drive channel**: rev 6 has ~85 parts per channel (per
gate: Miller-clamp FET, booster FET, two Zeners, Ron/Roff/R_KS, 10 k; per channel: DESAT string of 3 diodes, Miller
inverter, booster trigger, interlock stretcher, 3 × 22 µF …), i.e. 1,020 of the 1,850. Parts count is an assembly-cost
item (≈ 0.02 USD per placement), not a BOM item.

**Connectors between the boards:**
- **J1 power ↔ control, live ↔ live:** 2 × 30 board-to-board (XKB X9555-class): 12-16 PWM, EN, FLT_N, RDY,
  3-4 i_L, IA, IB (two gains), VA, VAX, VB, VBX, PE divider, 6-8 NTC, K_A/K_B/K_PRE commands + hold status, 2 IMD
  switches, bias enable, 24 V / 5 V / 3.3 V and 8 BUS- returns.
  *Correction 2026-10-05:* as drawn, the connector is 2 × 32 (contract `PC` in `gen/interfaces.py`, PV-PWR and PV-CTL),
  not 2 × 30. Since PV-PWR rev A2 it carries no 24 V or 5 V: those four pins carry the sensor references IL1R–IL4R
  (PV-CTL never used them; it takes 3.3 V only).
- **J2 SELV supply:** 2-pin from the AUX-T1 SELV rectifier (power board) to the control board's SELV zone, both ends
  ≥ 10 mm from live copper, double-insulated wires.
- Control board SELV zone: CAN in/out, RS-485 in/out, enable/status (pluggable Kefa terminal blocks), 3 fan headers,
  PE/shield. Live zone: debug header only.
- Power board ↔ chassis: press-fit / bolt terminals for the bus entries (A+, B+ after the contactors, A-, B- via the
  shunts) and 2 per inductor; coil leads (3 × 2-pin); heatsink NTC leads; terminal-side taps (A+_T, B+_T) brought onto
  the board edge at the rear by short links for the varistor networks, VAX/VBX, IMD and aux input.

---

## 11. What is reused unchanged (do not redraw)

| function | from | status in the cost-first boards |
|---|---|---|
| gate-drive channel: NSI6651, split Ron/Roff per device, R_KS, per-gate Miller clamp FET + inverter, SC booster, DESAT string, interlock stretcher, design_check() | `gen/gdrv.py` rev 6 `channel()` | **unchanged**, called 12 (16) times; only the bias block becomes external (`bias="ext"`, §4) |
| power stage: devices, leg decoupling, RC damper, bus layout rules (15 nH bulk-to-leg, 11.5 nH board + devices); bleeders become one 800 kΩ string per port (§8) | `gen/pvcell.py` rev C0 sheets 03_power / 04_bus, `cell_spec.json` | unchanged values; decoupling maker changes (re-run `pv_dpt_leg_dec.cir`, R-08) |
| local OC window logic (window comparator → latch → PWM gating) | `gen/pvcell.py` 05_sense / 02_logic | reused, fed by the TMR sensor instead of LA 150-P |
| varistor network, branch fuses, monitor loop, X/Y caps, PE_T strap | `gen/port.py` rev 6 | **unchanged** (the monitor opto output now goes to the live MCU directly) |
| precharge sizing, IMD two-state equations + 3-sample prediction | `sim/port_design.py` §1, §8 | method reused; precharge resistor and IMD switches change |
| HV input network, start-up cascode, brown-in, OV lockout, overload timer, UCC28C59 + SiC stage | `gen/aux_hv.py` rev C1 blocks 01-03 | reused; transformer (75 W, two secondaries) and output side redesigned |
| CMPSS backup window, ADC sampling plan, plausibility rules, MPPT, control loops | `sim/out/pv_control/control_spec.json`, `sim/out/pv_mppt/` | reused; ISR timing re-checked for 120 MHz (R-14) |
| CAN / RS-485 field protection (termination, TVS), fan tach/PWM conditioning, NTC conditioning | `gen/sys_io_aux.py` | reused on the SELV side / control board |
| build checks (ERC, netlist, part stress, domains, barriers, crossings), pin audit, cost model | `gen/dcdclib.py`, `gen/pin_audit.py`, `gen/cost.py` | used for both new boards; domains: HV_LIVE (BUS-), HV_SW (gate islands), SELV, PE |
| insulation requirement tables | `sim/insulation.py` | re-run with the new barrier list (B1: AUX-T1 + 5 isolators) |
| inductor, AUX transformer method, magnetics verification | `sim/magnetics.py`, `design_pv_inductor.json` | inductor unchanged; AUX-T1, bias transformer, CM core are new MAG-1/2 items |
| **dropped:** CTRL-C2000 (F28388D card), SYS-IO-AUX, BMU-GW, PV-PORT board, PVCELL cell logic + RS-422 CELL link, AUX-HV board as a separate board | — | stay in the repository as the roadmap implementation |

---

## 12. What the lean design gives up (plain list for the owner)

1. **Terminal-short survival** (48 clamp rectifiers): a bolted short at a port's terminals now probably destroys that
   port's legs; the module fails without fire (fuse / contactor) and is repaired.
2. **The PELV control island:** the controller and its debug header are at up to 1000 V from earth; service needs
   isolated probes; field updates go over CAN.
3. **The dual-channel safety chain and its fault analysis (75-row FMEA):** one latch; the external stop is a
   single-channel functional stop with no SIL/PL claim — if a cabinet needs a rated safety function, it must open its
   own DC switching devices.
4. **Self-sufficient fault coverage on the battery port:** the band 0.95-1.3 kA is left to the upstream battery
   protection (0.25 s) — §6.3. Full-range gBat fuses and the paralleled HVC43 pair are gone.
5. **The cabinet 24 V and redundant feeds:** the module is dark when both ports are below ~200 V.
6. **Features:** Ethernet, CAN FD (the MCAN exists, not wired), second CAN, second RS-485, 8 + 8 digital I/O, 12
   temperature channels, 4 fan channels → 1 CAN, 1 RS-485, 1 stop input, 1 status output, 7 (9) temperatures, 3 fans.
7. **Contactor auxiliary contact:** weld detection by a voltage test instead of a mirror contact.
8. **Active discharge:** passive bleeders, "wait 10 min" (15 min for PV-P100/110) instead of an active discharge.
9. **Margins:** Tj at 45 °C full power 78 → ~110 °C (efficiency −0.05 points at full load, derating from ~55 °C);
   gate-bias regulation ±2 % instead of the UCC14241's tighter loop and no per-channel power-good; inductor-current
   sensing 1.5 % open-loop TMR instead of 0.5 % closed-loop LEM; the fan's rated low temperature −10 °C instead of
   −40 °C; the precharge resistor 600 J instead of 2,300 J (3 attempts, then lockout); if the Faratronic second source
   is used, film capacitors rated 1200 V at 70 °C instead of 1300 V (about half the voltage-life margin, Faratronic
   only where the hot spot stays ≤ 70 °C).
10. **The common controller card** shared with other products (F28388D): the F280039C board is specific (the DAB can
    reuse it, §16).

---

## 13. Open risks

| # | risk | consequence | next step |
|---|---|---|---|
| R-01 | **Inductor cost** 80 USD estimate × 3 = 25 % of the BOM; no quote | budget missed (§14) | quote the rev-M1 construction; re-open the design for ≤ 30 USD if the quote is > 50 USD |
| R-02 | Sichain SG2M040170HJ: no qualification statement, price an estimate (RFQ) | release condition (D-043) | Sichain reliability data + quote |
| R-03 | HPE501 aR fuse: no price; Kt and the 75 % long-term rule read conservatively (147 A at 65 °C for 250 A); coordination with the contactor not simulated in time | gap or derating wrong | Hongfa quote + curve data; time-domain coordination study (release time 10 ms, fuse curve) |
| R-04 | HFE82V-300C/1000: no price; coil-to-mounting insulation not stated (now a basic HV-PE crossing); economiser hold at ~50 % voltage and making ~0.5 kA capacitive inrush to be confirmed; no aux contact | basic insulation or contact life unverified | Hongfa statement; alternative: insulating mounting plate |
| R-05 | Fan rated −10 °C vs PV-20 −30 °C | cold start outside the data sheet | Delta low-temperature option or firmware rule |
| R-06 | Per-phase gate-bias transformer is a new custom magnetic: PD-free ≥ 1.75 kVpk between secondaries, C ≤ 5 pF, ±2 % rails over load | gate rail / Miller margin | MAG-1/2 spec, OpenMagnetics check, PD test on samples |
| R-07 | TMR sensors: no dv/dt immunity figure at 124 V/ns, no price | false OC trips or missed trips | Sinomags / CHIPSENSE data + quote; bench dv/dt test |
| R-08 | Chinese film capacitors: no price; leg decoupling ESL/ESR differ from C4AQ | decoupling peak current, overshoot | re-run `sim/spice/pv_dpt_leg_dec.cir`; quotes |
| R-09 | B1 isolators: CA-IS3062W / CA-IS3082W / CA-IS3821 reinforced certificates and VIOWM ≥ 1100 V DC not yet read; WB packages need the PD1 coating; CA-IS3417WT certification "in progress" | reinforced claim unproven | download data sheets/certificates; WW variants where they exist |
| R-10 | Heatsink NTC probes bridge live control and PE: need ≥ 2.2 kV rms lead-to-lug | basic insulation | choose a probe with a stated test voltage |
| R-11 | EMI: estimate 106-112 dBµV vs limits recalled from memory | 1 or 2 cores, or a wound choke (+20-30 USD) | early pre-compliance scan; buy CISPR 11 |
| R-12 | Standard values from memory (reinforced 8 kV vs 6 kV credit, creepage tables, IEC 62109-2 33 kΩ rule) | barrier dimensions | buy EN 62477-1 / IEC 62109-1/-2 (D-032 open item) |
| R-13 | AUX at 75 W from 200-1100 V with one 1700 V SiC: drain stress (1100 V + reflected + spike ≤ 1445 V) and a bigger reinforced transformer | aux redesign effort | re-run `sim/aux_hv_design.py` at 75 W |
| R-14 | F280039C at 120 MHz: CLA/CPU budget for 4 phases (old budget was for 200 MHz) | control timing | firmware timing estimate before the pin plan |
| R-15 | Parts count ~1,850 vs ~1,000 target | assembly cost (+17 USD) | channel review is outside D-044 |
| R-16 | Hold-off needs the shunt path to read ±1.5 kA | contactor rule | second gain path, verified in the board design check |
| R-17 | PV-P100/110 thermal with 3 fans in 444 mm | earlier derating | own thermal run |
| R-18 | Megarevo standby < 20 W met only by estimate (≈ 15 W) | marketing figure | measure on the prototype |

---

## 14. Cost summary (from `gen/data/costfirst_bom.csv`)

| block | PV-P75 (USD) | PV-P100/110 (USD) | largest items |
|---|---|---|---|
| POWER | 450.24 | 600.02 | 3 inductors 240.00, 24 SiC 97.68, 12 port film 64.80, 24 AlN pads 24.00 |
| PORT B (battery) | 125.11 | 131.11 | contactor 55.00, 2 aR fuses 36.00, precharge relay 12.71 |
| GATE DRIVE | 78.72 | 104.95 | 12 NSI6651 35.74, channel discretes 31.20, bias 11.78 |
| PORT A (PV) | 71.70 | 77.70 | contactor 55.00, 2 terminals 16.00 |
| THERMAL | 60.45 | 71.40 | 3 fans 38.55, heatsink 21.00 |
| SURGE + EMI | 58.80 | 58.80 | 4 branch fuses 24.00, X caps 9.00, 6 varistors 7.20, CM cores 12.00 |
| AUX SUPPLY | 34.32 | 34.32 | input network 12.80, transformer 8.00 |
| SENSING | 31.00 | 37.00 | 3 TMR sensors 15.00, divider strings 7.50 |
| MECH-ELEC | 29.30 | 34.96 | busbars 20.00 |
| CONTROL | 9.19 | 9.49 | F280039C 4.40 |
| IMD | 8.80 | 8.80 | 2 CA-IS3417WT 4.00 |
| INTERFACE | 8.09 | 8.09 | CA-IS3062W 1.73 |
| **total BOM** | **965.72 (12.9 USD/kW)** | **1,176.64 (11.8 USD/kW at 100 kW, 10.7 at 110 kW)** | |
| budget | 800 → **+166 USD (+21 %)** | — | |
| today (`bom/COST.md`) | 2,788.76 → **−65 %** (today's figure leaves 24 lines unpriced, among them the 24 SiC MOSFETs ≈ 98 USD) | 3,342.30 → −65 % | |
| evidence | high 45.6 (5 %), medium 90.8 (9 %), **low 829.3 (86 %)** | | |
| Chinese-volume view (assumptions: inductor 55, contactor 38, aR fuse 12, NSI6651 2.20, fan 8.50, SiC −15 %, AlN −40 %, custom metal −20 %, everything else −10/−15 %) | **≈ 736 (9.8 USD/kW)** | ≈ 898 | |
| outside the BOM (rough, `gen/cost.py` rules: 0.65 cm² per part at 0.045 USD/cm², 0.02 USD per placement + 4 USD per board, enclosure 90, final test 55) | ≈ 245 (PCBs 54, assembly 45) vs 350 today | | |

**The 800 USD budget is not met at catalogue prices** (966 USD), and the 550-600 USD expectation is not met at volume
(~736 USD). What would have to go next, in the order I would take it:

| step | saving (catalogue) | what it costs in function |
|---|---|---|
| 1. Re-open the inductor for cost (target ≤ 30 USD: e.g. one stacked E-core of Chinese powder with round litz, accepting more loss) | ≈ −150 | +10-20 W per phase (−0.04 … −0.08 % at full load); a new MAG-1 verification; **this alone brings the module to ≈ 816 USD** |
| 2. AlN → Al2O3 0.635 mm pads | −18 | Tj +2-3 K; needs the PD test re-done |
| 3. Standard panel terminals instead of custom stud feed-throughs | ≈ −16 | none if PD3 creepage is kept |
| 4. Asian 10×38 gPV branch fuses (Hollyland HC10gPV) in the varistor network | ≈ −16 | re-coordination of the frozen network (I²t margin 1.65× instead of 3.6×) |
| 5. Remove the PV-port contactor | −56 | **not advised:** a reversed array or a failed-short module is then fed by the array until someone opens the array isolator — a fire risk |

Steps 1-4 reach ≈ 766 USD at catalogue (≈ 580-600 USD at volume).

---

## 15. Changes against the D-044 direction (where I refined or disagree)

1. **PV port keeps one contactor** (the direction left it open): reverse polarity and isolation of a faulted module
   from a current source that no upstream device clears are worth 56 USD.
2. **Battery port: aR fuse + a contactor that may break faults up to 1.0 kA** (HFE82V-300C/1000: 1.5 kA once at
   1000 V). This shrinks the band left upstream from "contactor breaking capacity to fuse fast region" to
   **0.95-1.3 kA within 0.25 s**.
3. **Fans and communication share one reinforced SELV domain fed by a winding of the single aux transformer**; the
   live rail needs no optocoupler. No separate isolated DC/DC module anywhere.
4. Refinements: the heatsink stays earthed (not BUS-); contactor coils are live (coil-to-mounting becomes a basic
   crossing — R-04); the IMD uses two isolated SiC SSRs (CA-IS3417WT) referenced to the live controller.
5. **Disagreements:** (a) **800 USD is not reachable while the inductor is frozen** at its 80 USD estimate; (b)
   **~1,000 parts is not reachable with the frozen gate-drive channel** (~85 parts per channel); (c) **one board is
   not justified** (§10).

---

## 16. DAB-D60 on the same principles

Today (`sim/out/dab_design/report.md` §0, `dab_spec.json`, `bom/COST.md`; corrected 2026-10-05, D-068): 60 kW
isolated DAB, 2 full bridges, 100 kHz, two-unit transformer (186 USD est.) + series inductor (86 USD est.), liquid cold
plate. The **drawn DAB60 rev B0 has one CBB011M12GM4T per bridge** (UCC21710, +15 / −4 V): **BOM 3,615 USD** (60 USD/kW,
`bom/COST.md` DAB-D60-FULL, catalogue) with DD600N16K clamps 785, NH fuses 494, CBB011M12GM4T modules 403, HVC43
contactors 163, flow switch 131, thermostat 69, HF capacitors 100. The **device study (not drawn)** proposes 2 paralleled
1200 V discretes per switch, **8 × IV3Q12013T4Z / SG2M014120LJ per bridge** (7.31 USD each; switches + insulators
145 USD per module against the modules' 403, report §0.3).

**What changes with the same principles:** the controller sits on **port 2's negative** (battery side); bridge-2
drivers and sensing are functional, as in the PV module. **Port 1 is a second DC system**: the transformer and every
part bridging the ports need **basic** insulation at 1850 V DC (D-032: port 1 ↔ port 2 basic, PD ≤ 10 pC at
3149 Vpk) — so bridge-1 bias needs one per-bridge transformer with a basic 1850 V DC barrier (still cheaper than
4 UCC14241), and V1 / I1 cross that barrier once (CA-IS1311BG + CA-IS3115AW for V1, one TMR sensor for I1). The
single reinforced B1 barrier to SELV stays. Both ports face stiff sources (PCS DC link, battery) → both are
battery-type ports (aR fuse pair + HFE82V + precharge). No clamp banks (−785 / −53 USD). The coolant flow switch and
the thermostat become two NTCs (inlet/outlet ΔT) with a comparator. HF capacitors: Chinese PP film (Faratronic class)
instead of 20 × 47 nF C0G MLCCs per bridge.

| block (lean DAB-D60, estimate) | USD |
|---|---|
| 16 SiC 1200 V + insulators (dab report §0.3 "switches") | 145 |
| transformer + series inductor (estimates, unchanged) | 272 |
| HF capacitors (PP film instead of C0G MLCC) + port DC-link film (2 × 4 Chinese 45-65 µF) | 85 |
| gate drive: 8 NSI6651 channels + 2 bias transformers (one with a basic 1850 V barrier) | 55 |
| two battery-type ports: 2 HFE82V, 4 HPE501 aR, 2 precharge relays + resistors, coil drivers, 4 terminals | 250 |
| surge + EMI: 2 varistor networks, X/Y caps, 2 CM cores | 60 |
| sensing (port-2 dividers/shunt, isolated V1, TMR I1 and transformer current), IMD | 35 |
| aux supply (port 2 tap; port 1 tap would need a basic barrier), control board (same F280039C board), interface | 75 |
| cold plate (estimate, unchanged), 2 coolant NTCs, busbars, harness | 160 |
| **total** | **≈ 1,140 USD ≈ 19 USD/kW** (−68 % vs 3,615; +20 % vs its 950 USD working budget) |

The DAB stays well above the PV module per kW, as COST-REVIEW §6 expected: its 272 USD of custom magnetics and the
120 USD cold plate have no equivalent in the non-isolated module, and two stiff-source ports cost twice the protection.
Its control board can be the PV control board (16 ePWM, 4 CMPSS, same SELV interface) with a different pin plan;
reaching 950 USD needs about −190 USD, which can only come from the custom magnetics (272 USD estimate, no quote) or
from sharing one protected port with the PCS. Nothing here is designed: it is a block estimate.
