vectivolt/PCM/sim/out/aux_hv_design/loop_bode.png

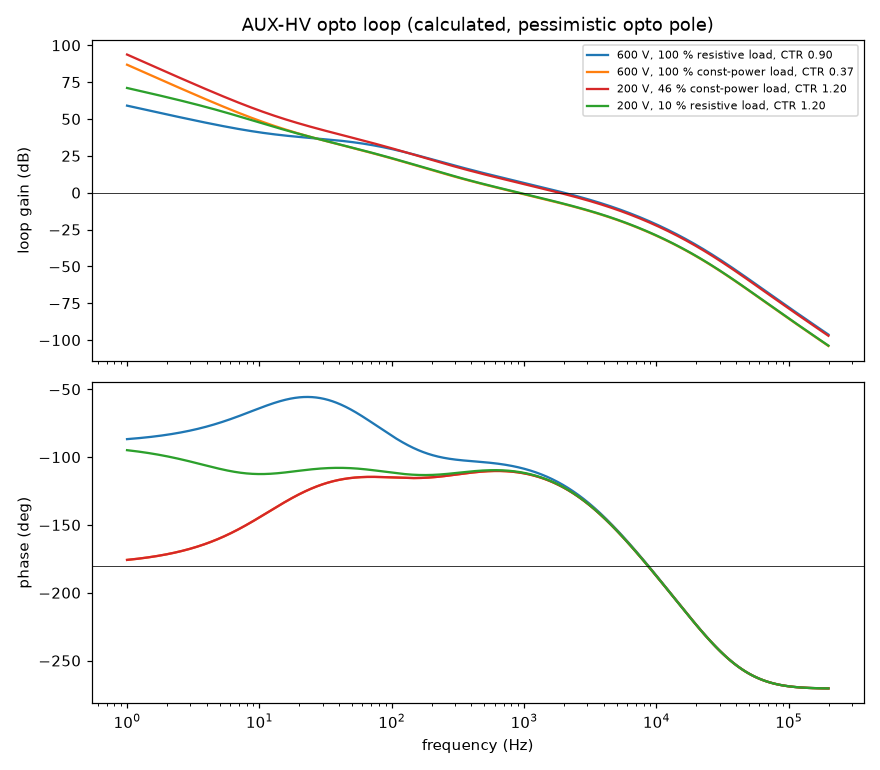
sim/out/aux_hv_design/loop_bode.png
