vectivolt/PCM/sim/out/aux_hv_design/losses.png

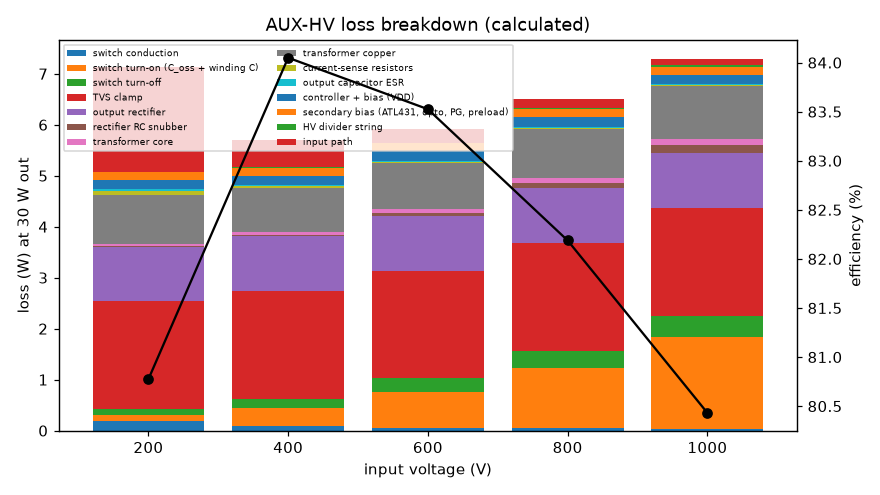
sim/out/aux_hv_design/losses.png
