vectivolt/PCM/sim/out/aux_hv_design/spice_short.png

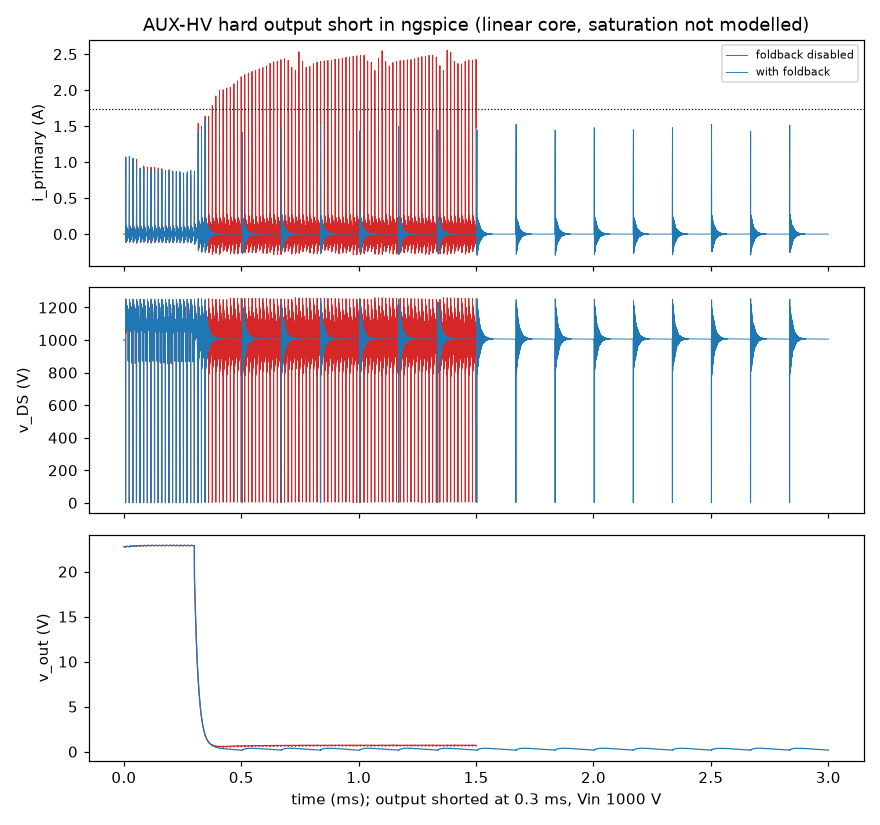
sim/out/aux_hv_design/spice_short.png
