vectivolt/PCM/sim/out/aux_hv_design/spice_surge.png

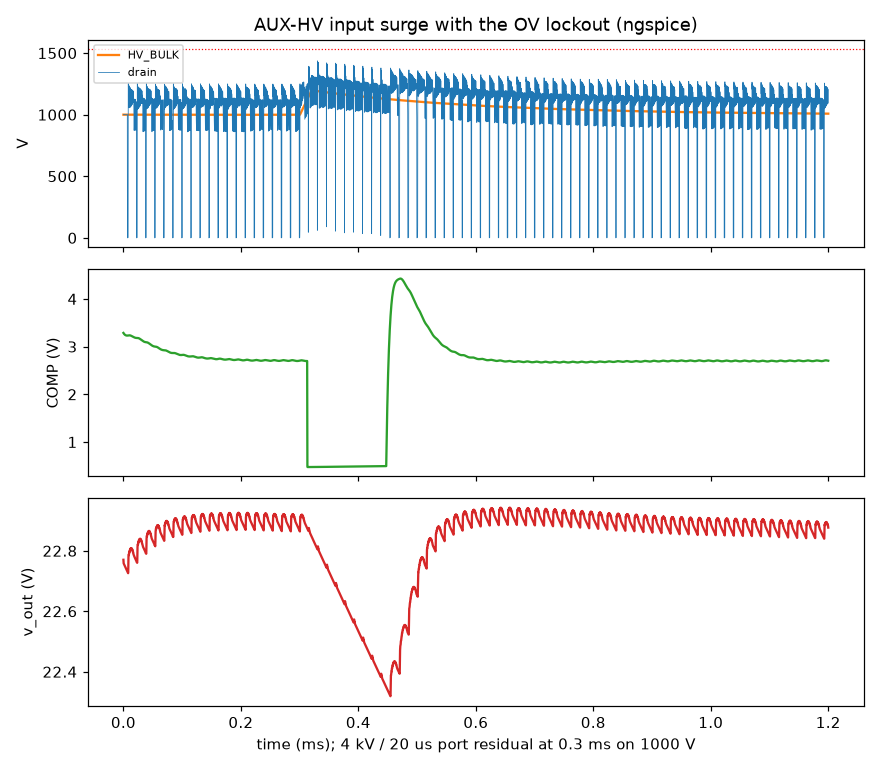
sim/out/aux_hv_design/spice_surge.png
