vectivolt/PCM/sim/out/aux_hv_design/spice_waveforms.png

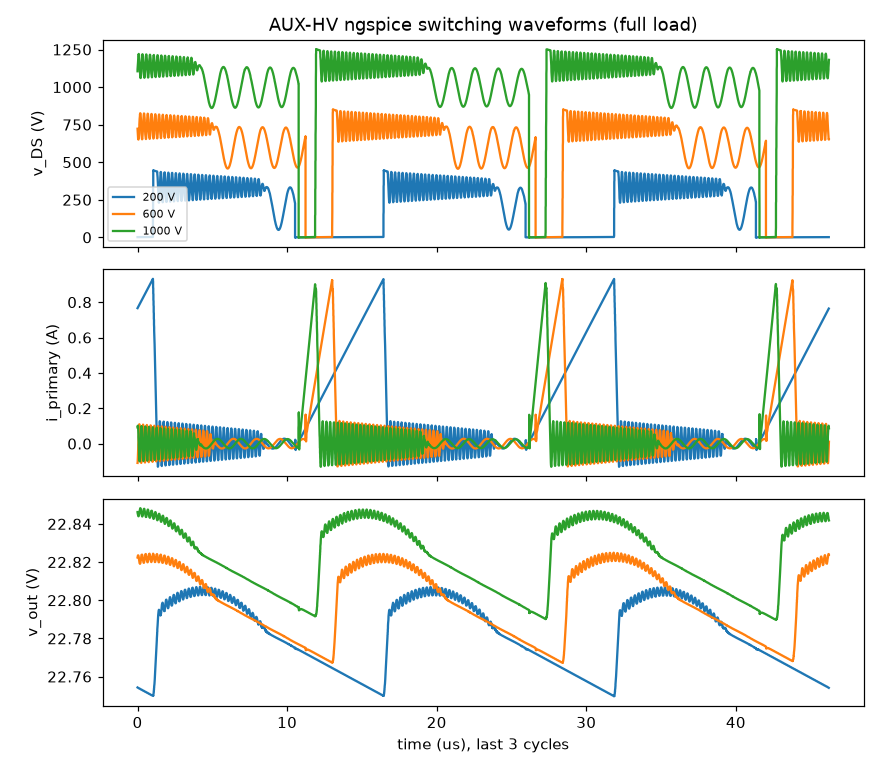
sim/out/aux_hv_design/spice_waveforms.png
