vectivolt/PCM/sim/out/aux_hv_design/system_start.png

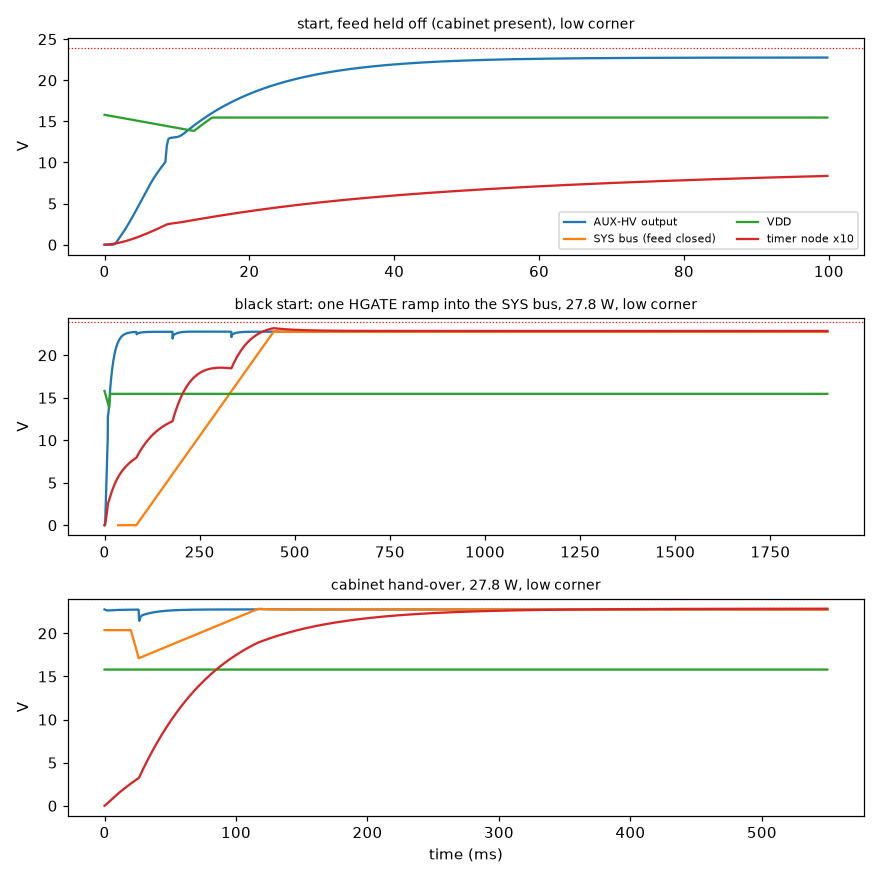
sim/out/aux_hv_design/system_start.png
