vectivolt/PCM/sim/out/dab_control/branch_fault.png

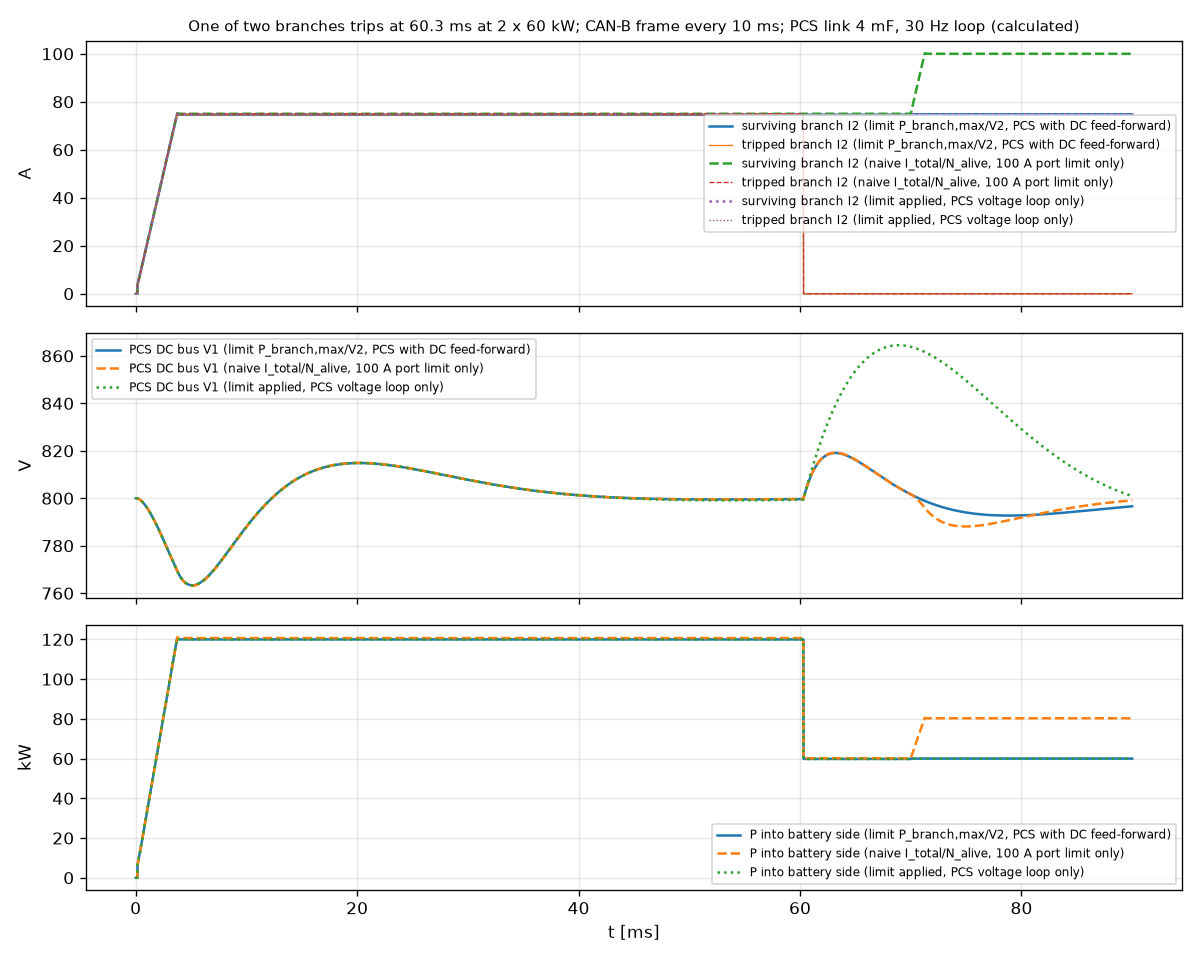
sim/out/dab_control/branch_fault.png
