vectivolt/PCM/sim/out/dab_control/parallel_sharing.png

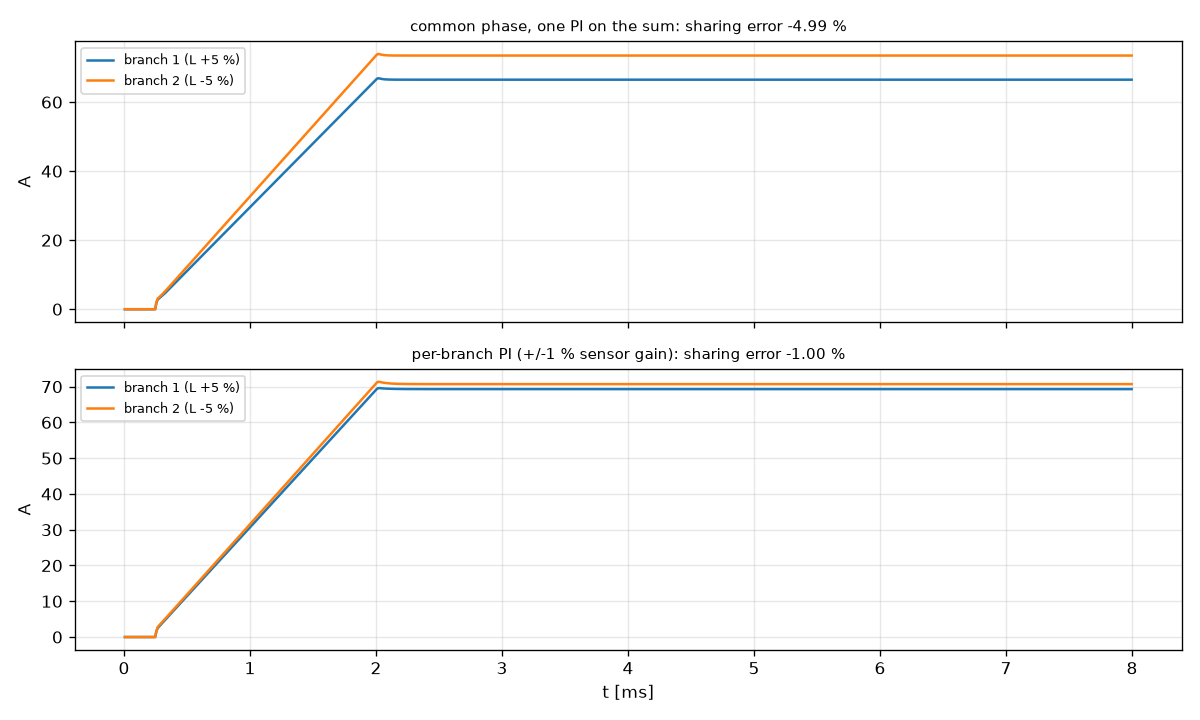
sim/out/dab_control/parallel_sharing.png
