vectivolt/PCM/sim/out/dab_control/pcs_link.png

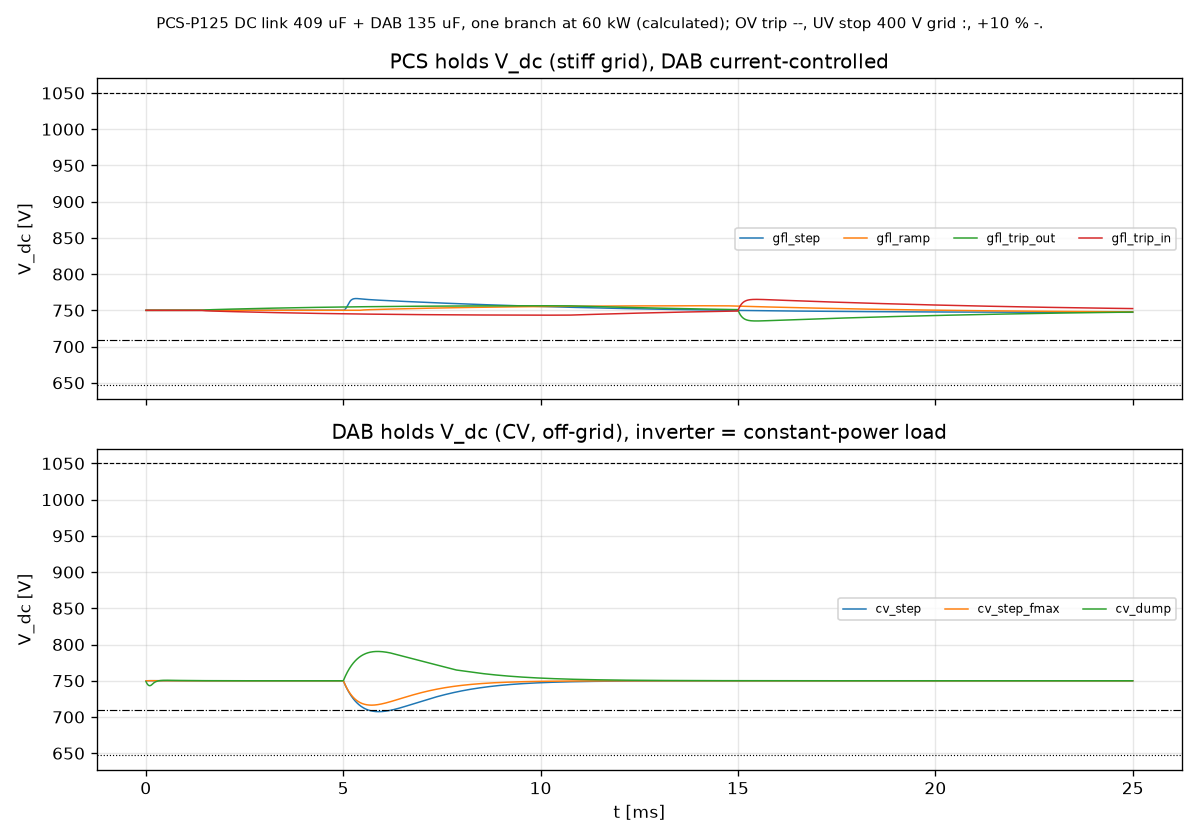
sim/out/dab_control/pcs_link.png
