vectivolt/PCM/sim/out/dab_control/power_reversal.png

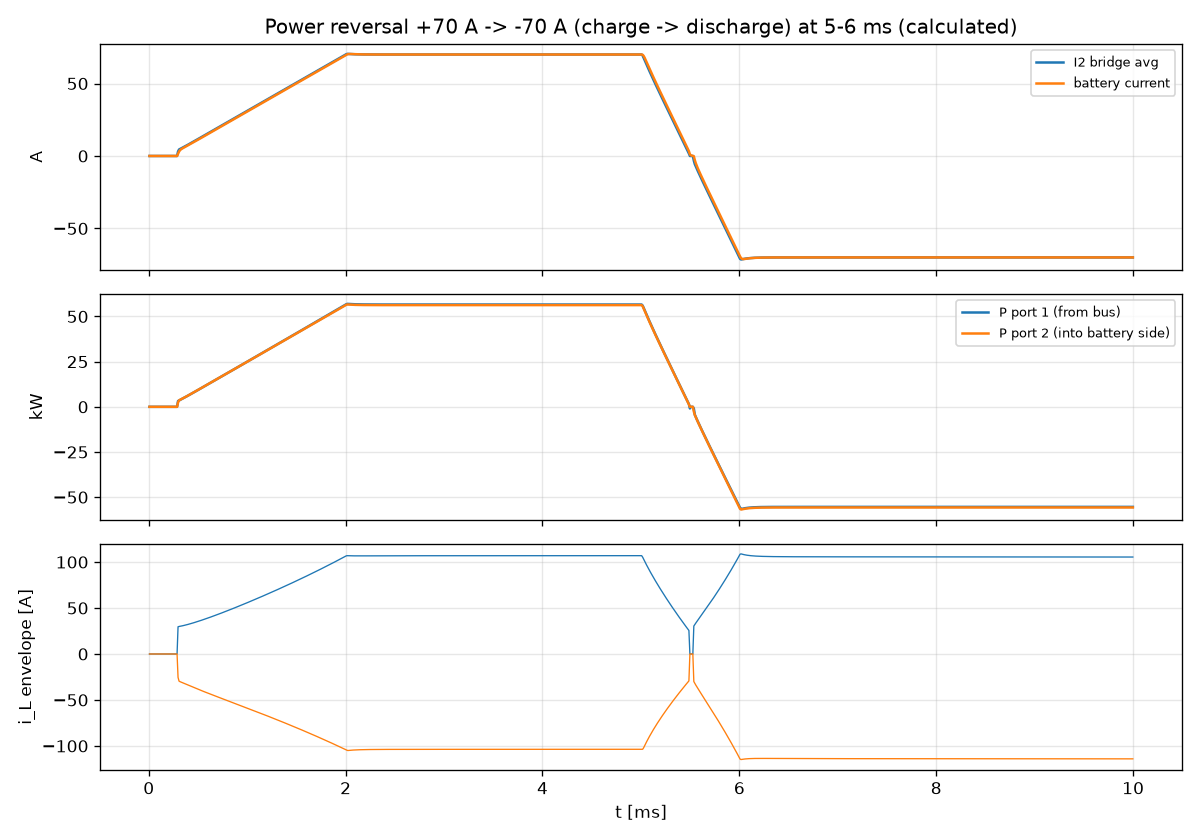
sim/out/dab_control/power_reversal.png
