vectivolt/PCM/sim/out/dab_control/softstart_cc.png

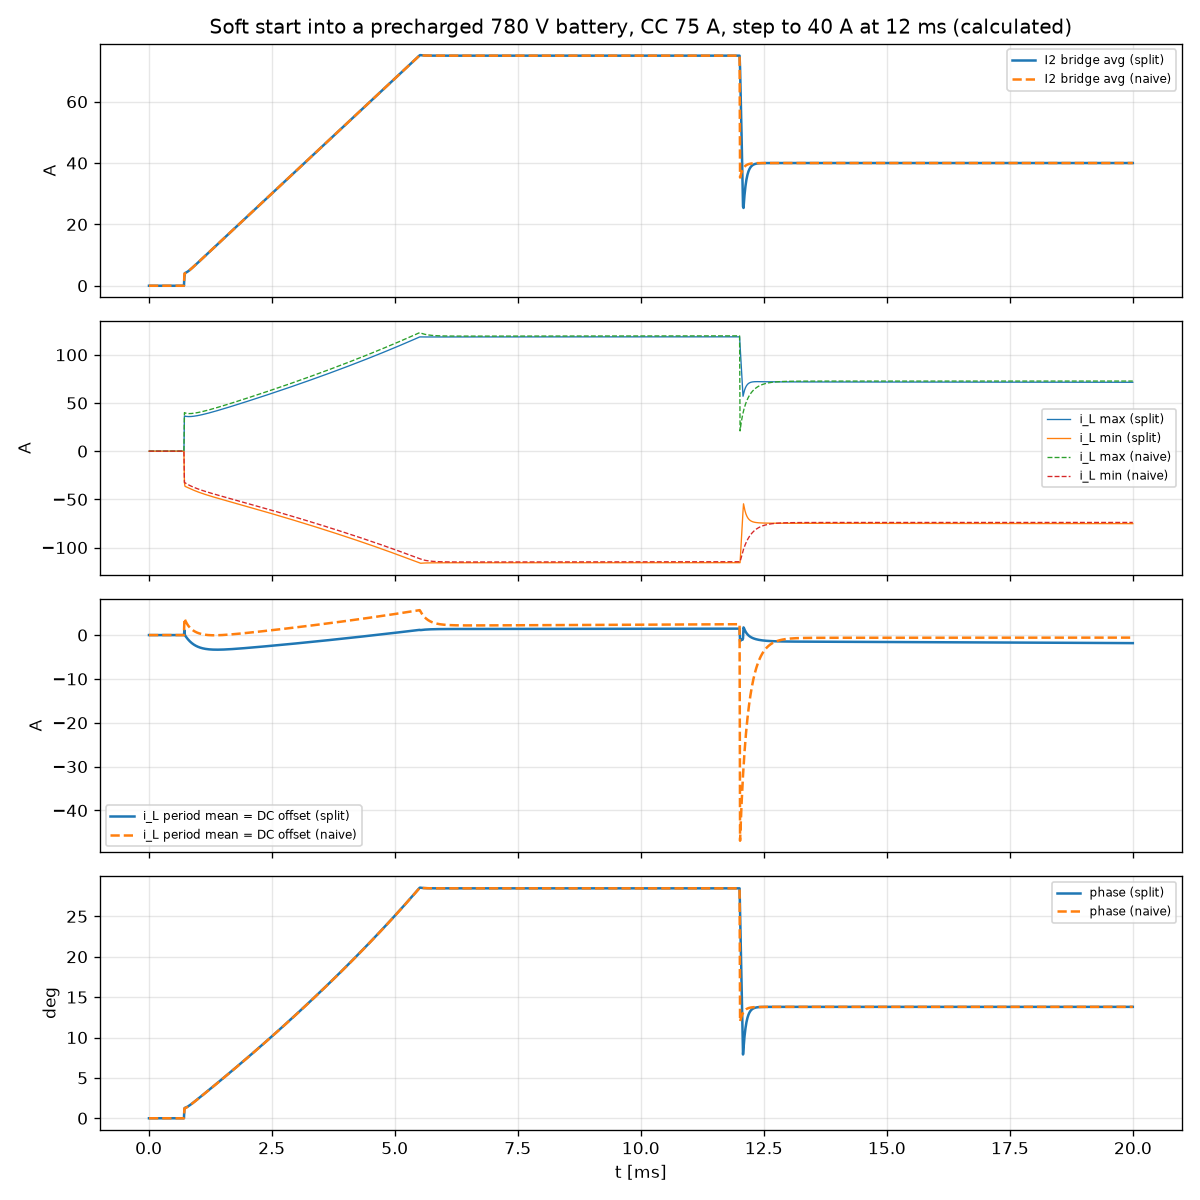
sim/out/dab_control/softstart_cc.png
