vectivolt/PCM/sim/out/dab_design/power_vs_phase.png

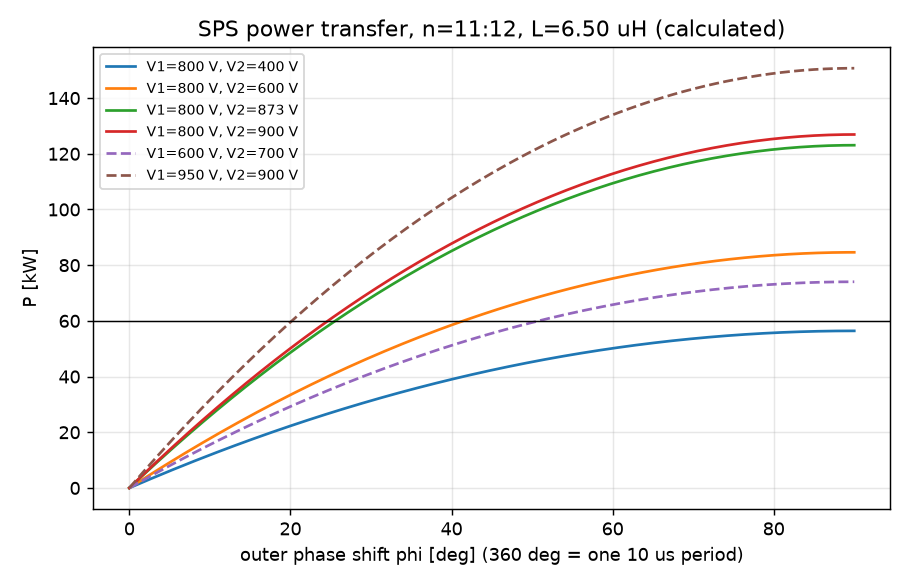
sim/out/dab_design/power_vs_phase.png
