vectivolt/PCM/sim/out/dab_design/spice_vs_analytic.png

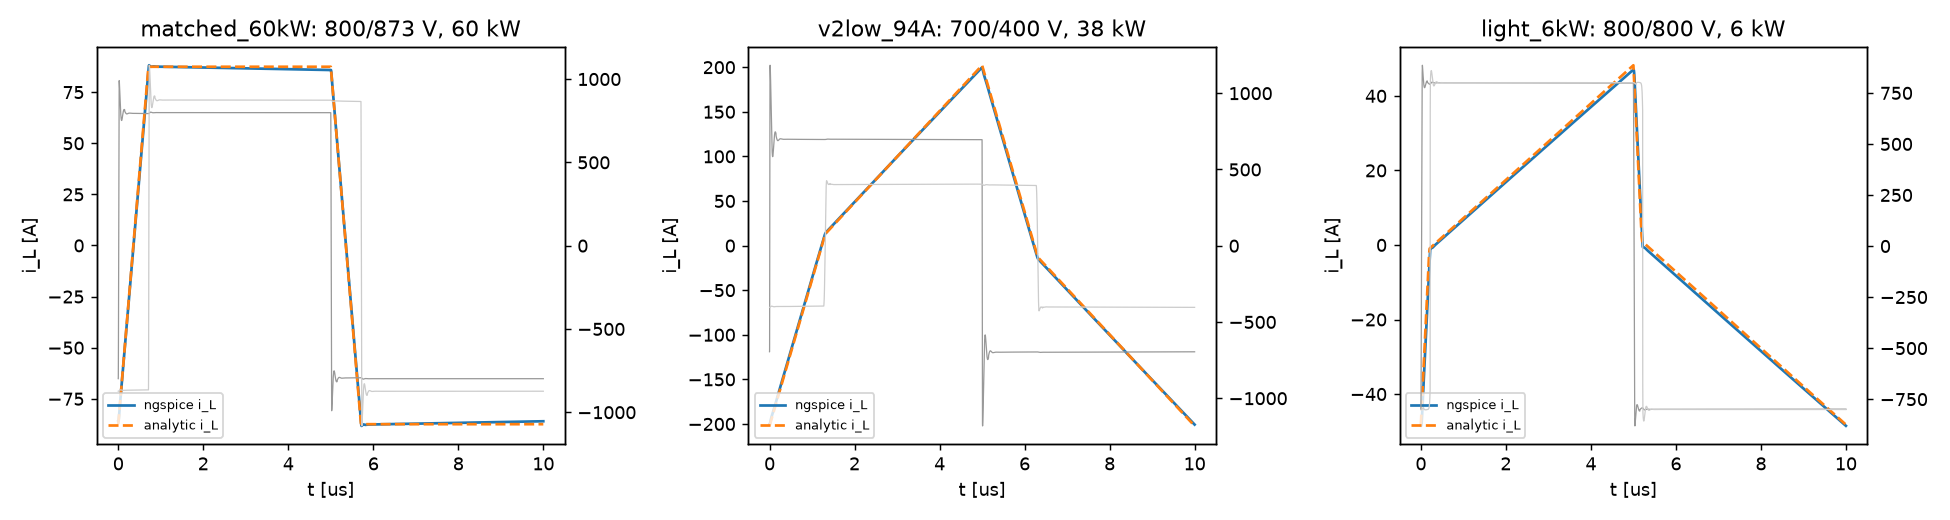
sim/out/dab_design/spice_vs_analytic.png
