vectivolt/PCM/sim/out/pcs_control/bode_scr.png

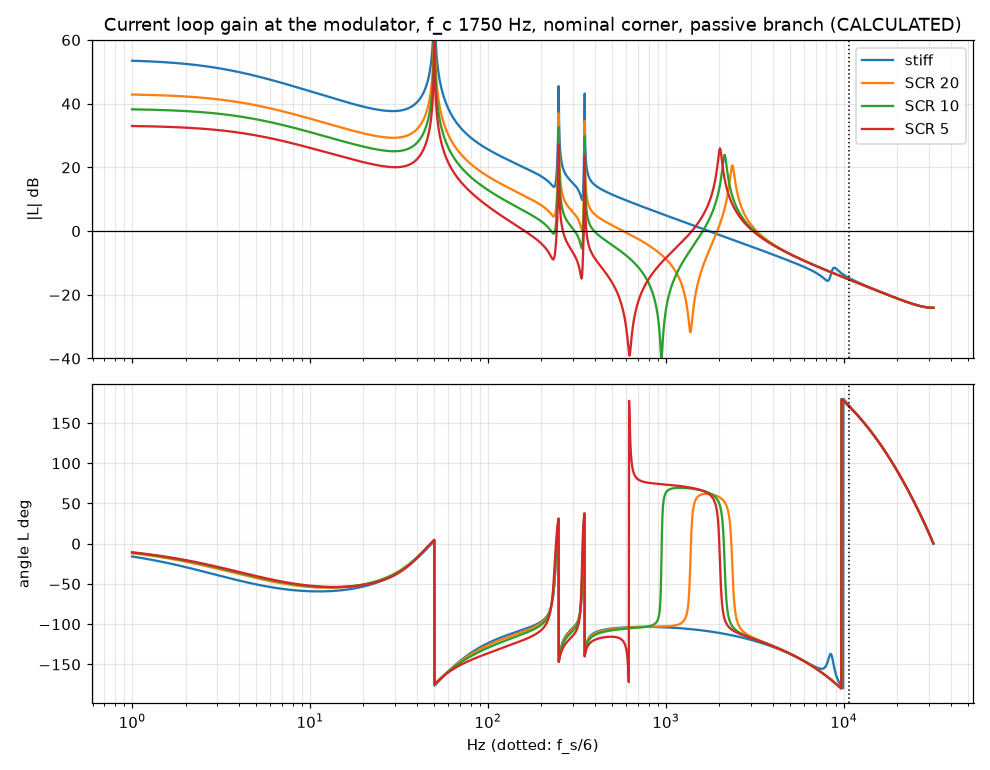
sim/out/pcs_control/bode_scr.png
