vectivolt/PCM/sim/out/pcs_control/bounded.png

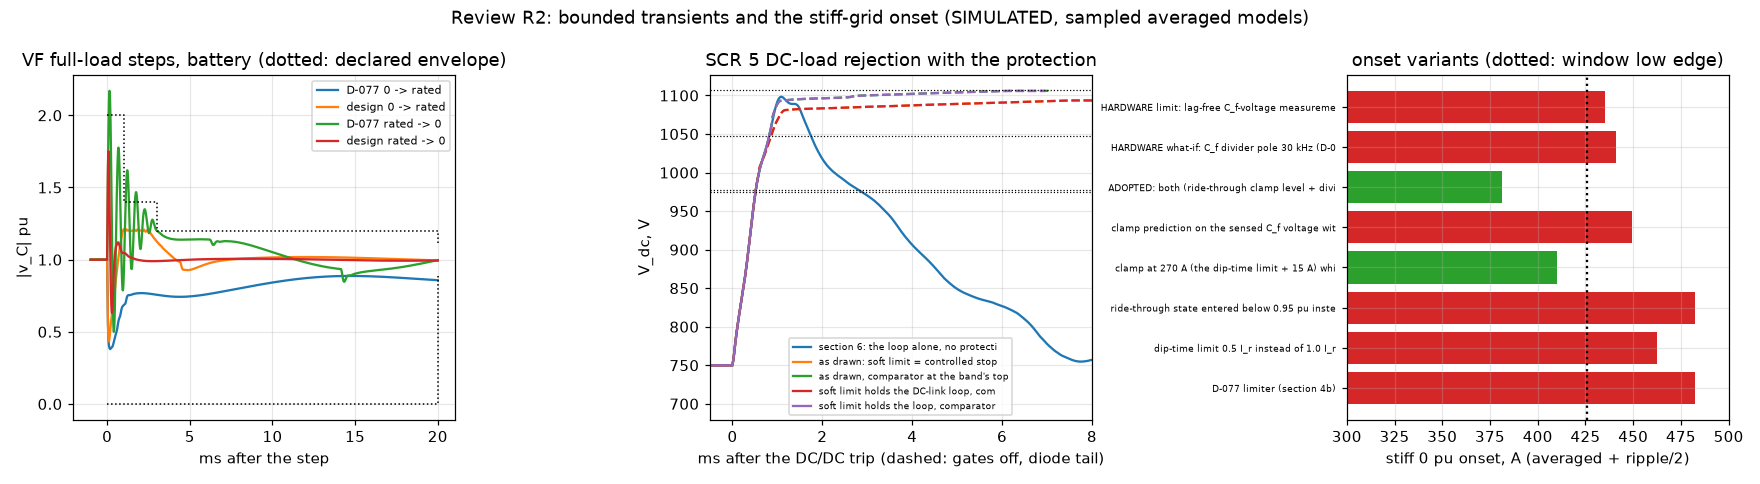
sim/out/pcs_control/bounded.png
