vectivolt/PCM/sim/out/pcs_control/faults.png

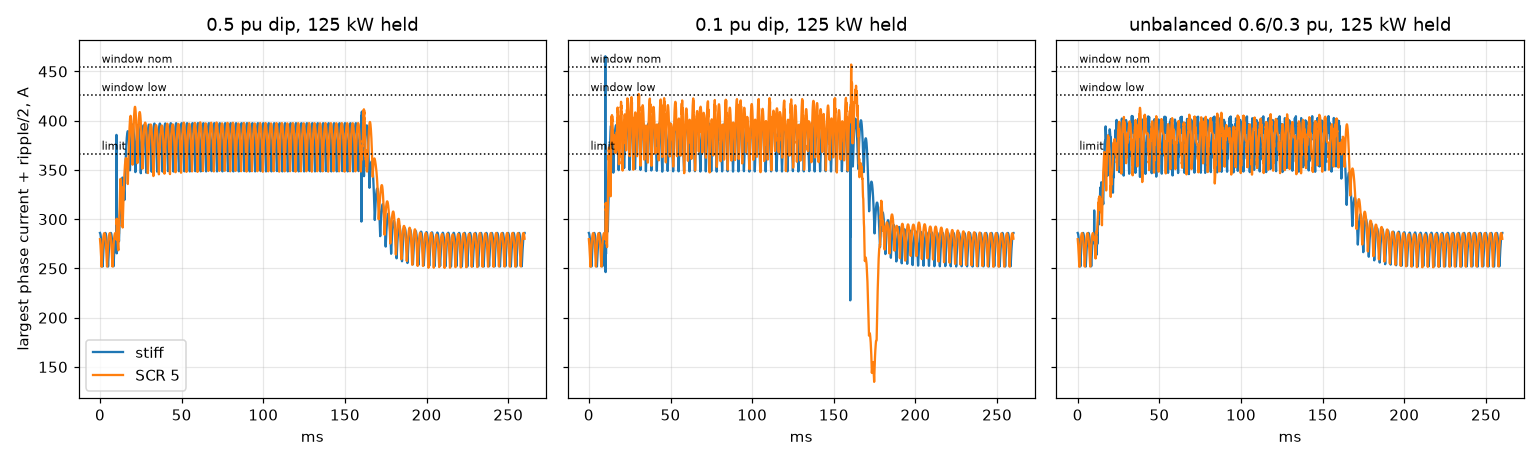
sim/out/pcs_control/faults.png
