vectivolt/PCM/sim/out/pcs_control/gfm.png

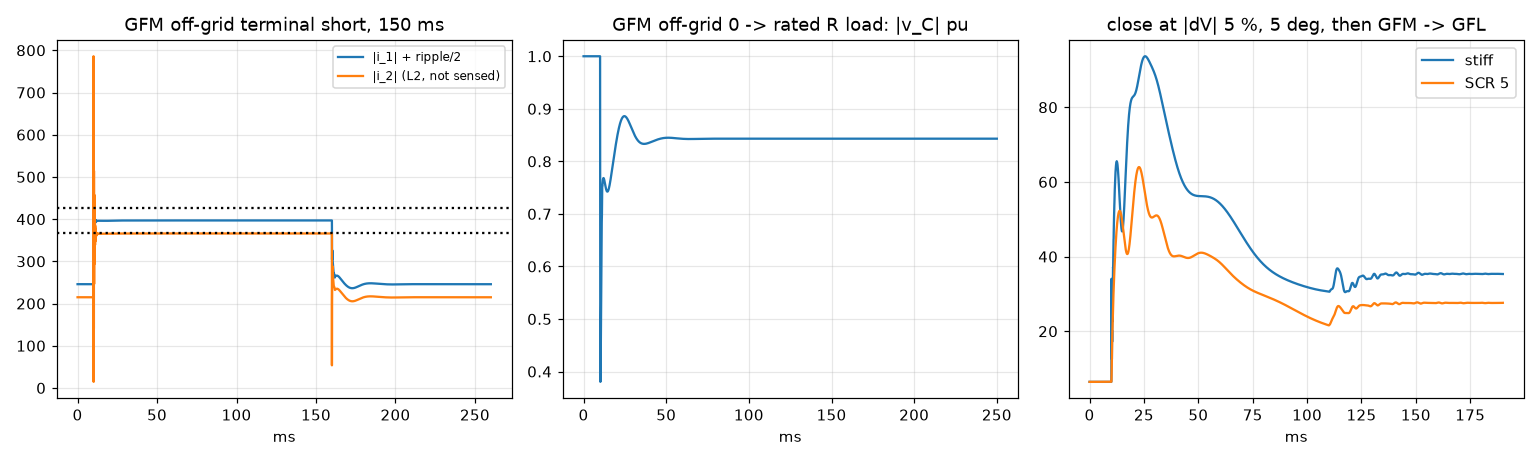
sim/out/pcs_control/gfm.png
