vectivolt/PCM/sim/out/pcs_control/pll_weak_grid.png

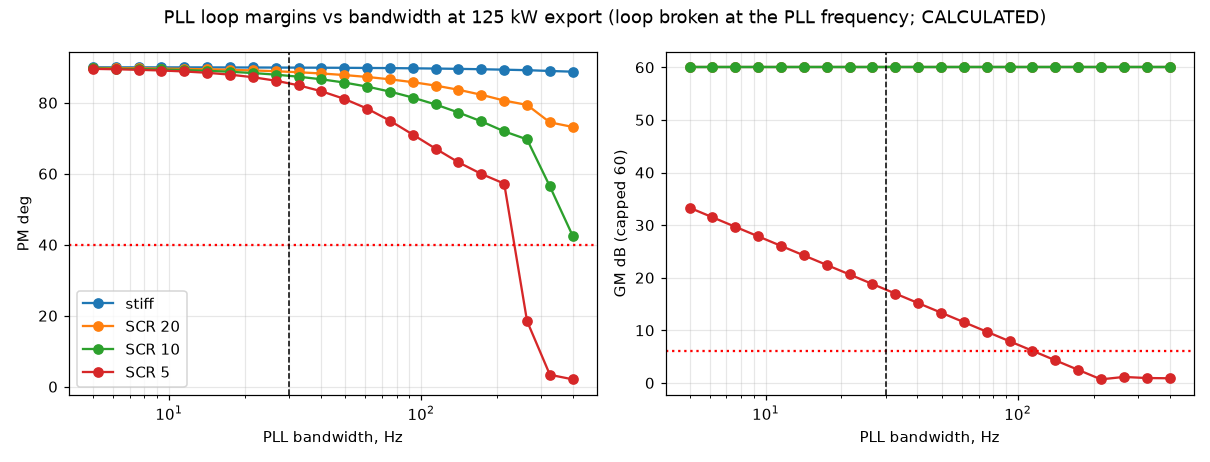
sim/out/pcs_control/pll_weak_grid.png
