vectivolt/PCM/sim/out/pcs_control/vf_and_ride_through.png

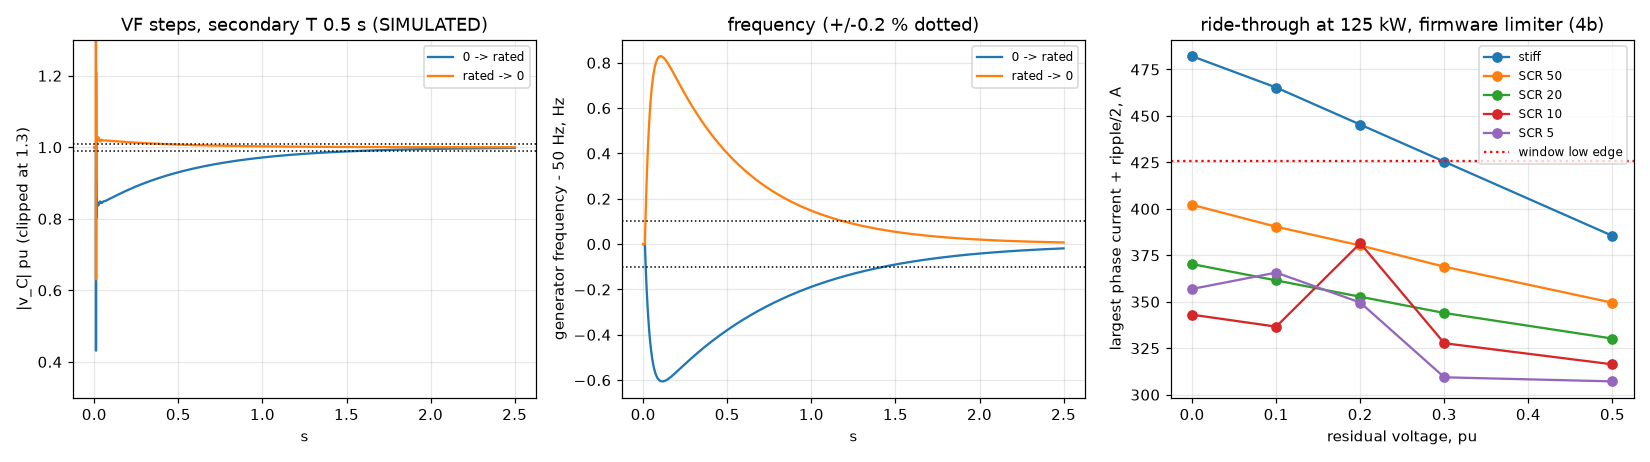
sim/out/pcs_control/vf_and_ride_through.png
