vectivolt/PCM/sim/out/port_design/imd_error.png

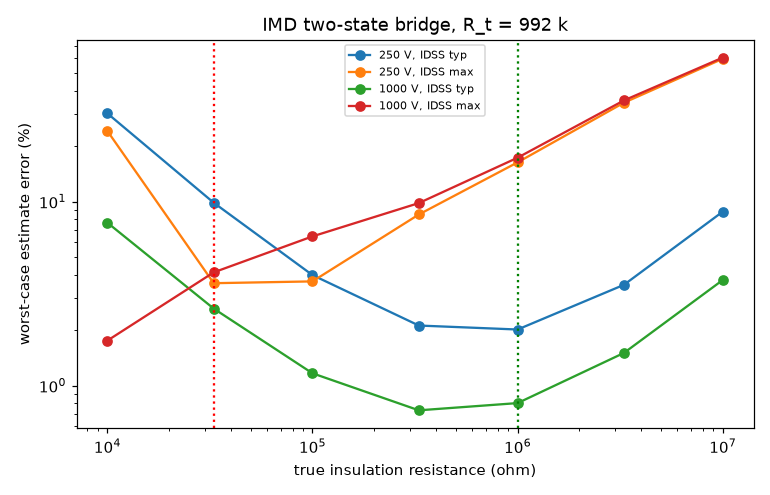
sim/out/port_design/imd_error.png
