vectivolt/PCM/sim/out/port_design/port_design.png

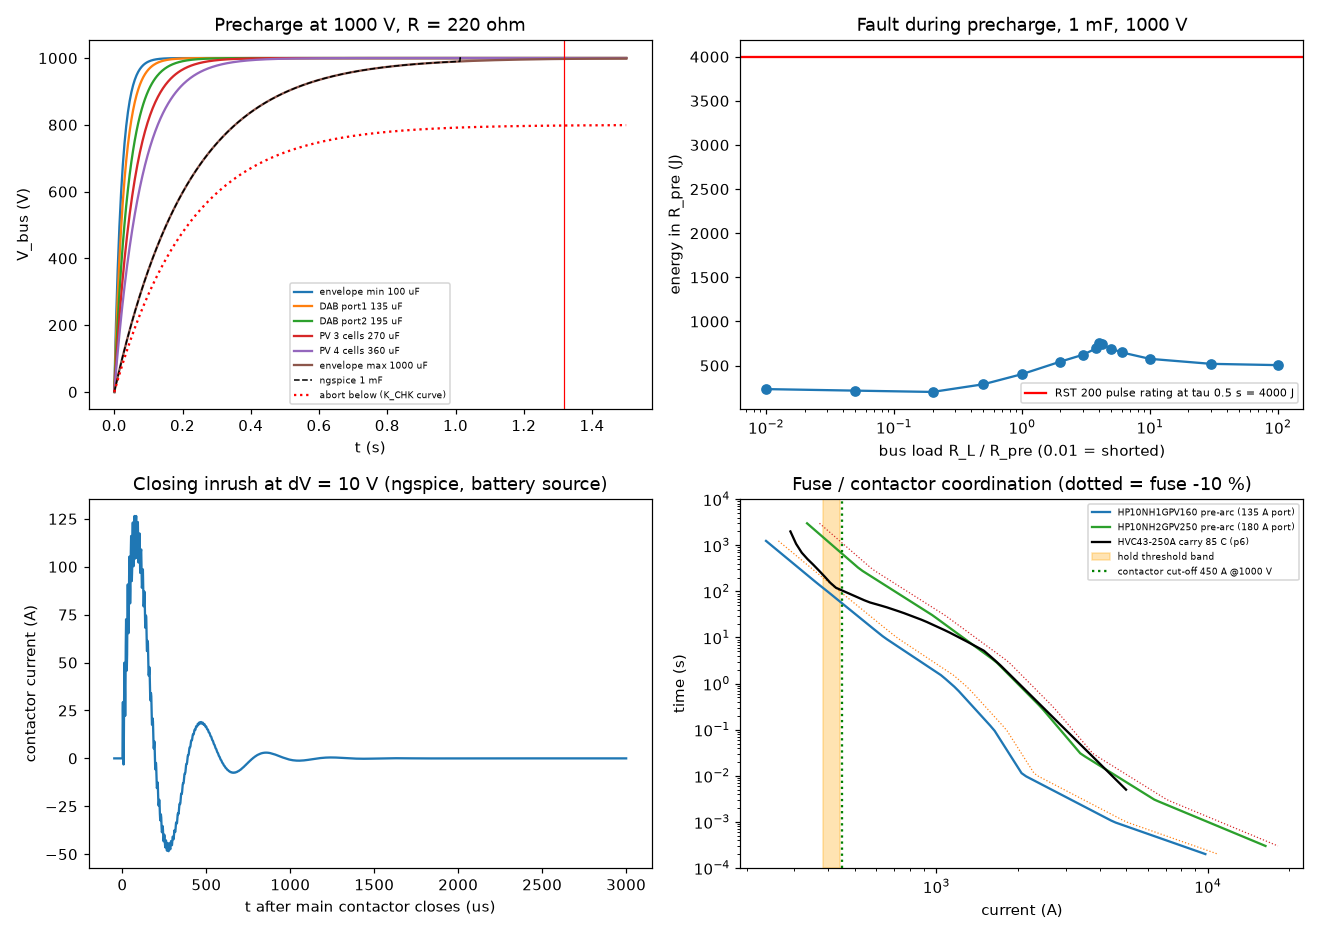
sim/out/port_design/port_design.png
