vectivolt/PCM/sim/out/pv_design/module_cooling_derating.png

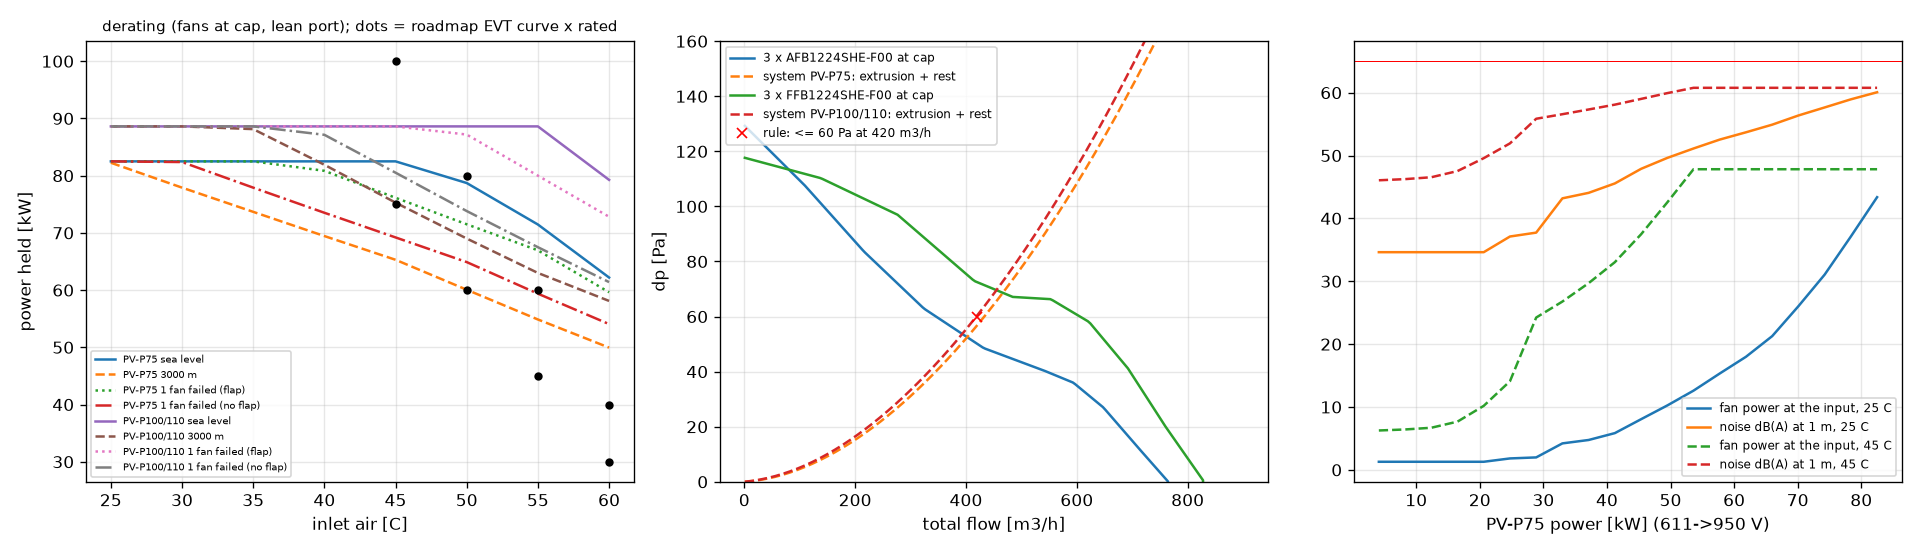
sim/out/pv_design/module_cooling_derating.png
