vectivolt/PCM/sim/out/pv_design/module_efficiency_maps.png

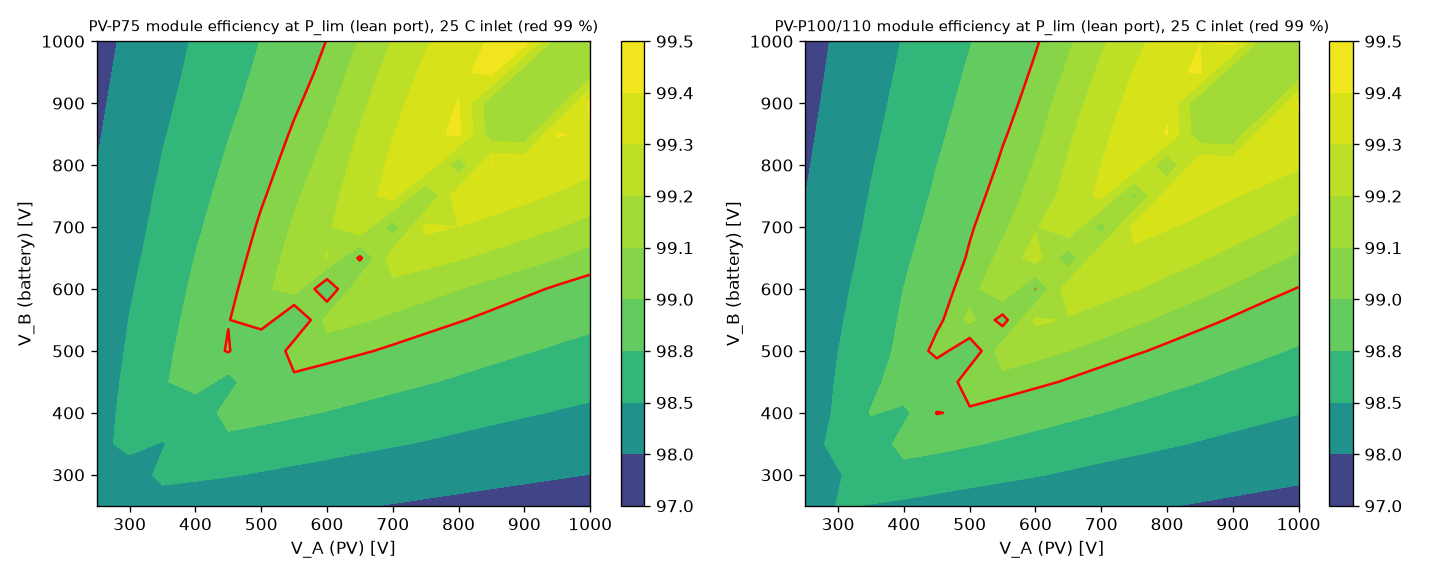
sim/out/pv_design/module_efficiency_maps.png
