vectivolt/PCM/sim/out/pv_mppt/array.png

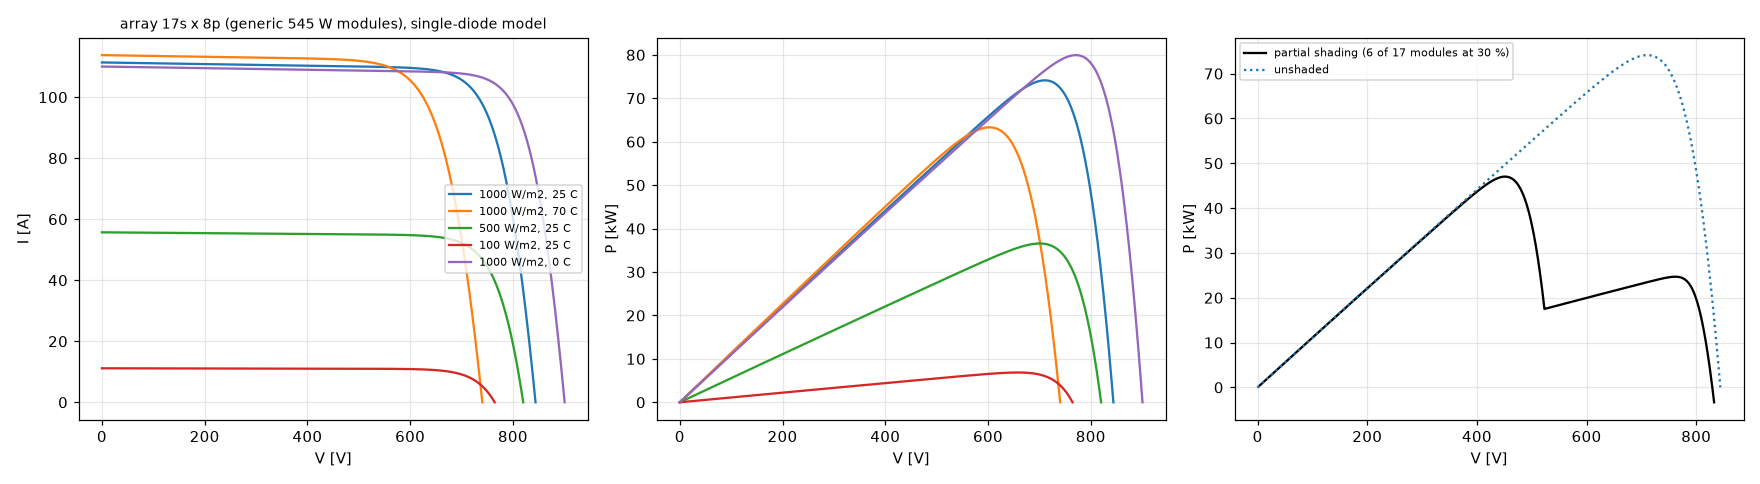
sim/out/pv_mppt/array.png
