vectivolt/PCM/sim/out/pv_tradeoff/efficiency_maps.png

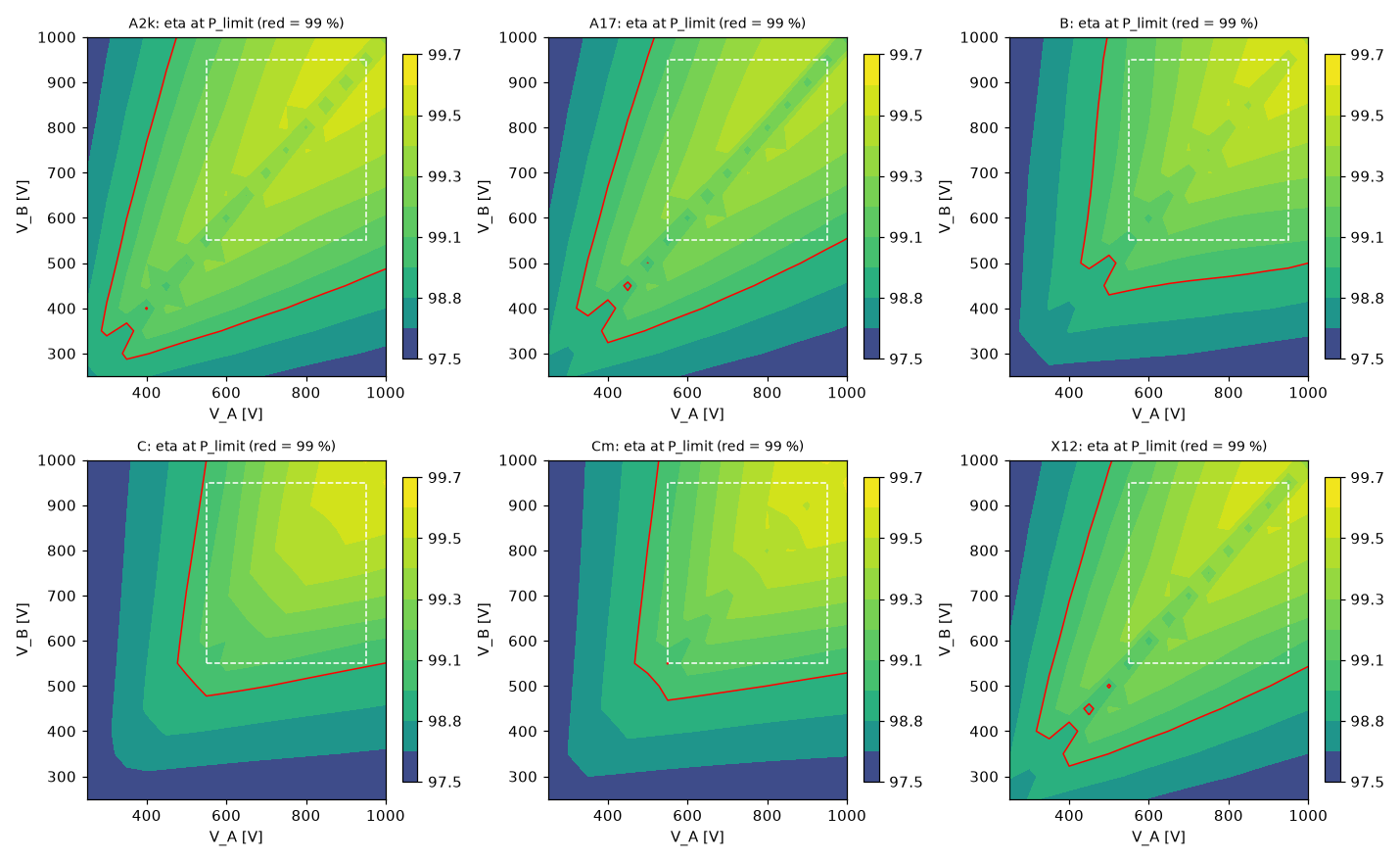
sim/out/pv_tradeoff/efficiency_maps.png
