vectivolt/PCM/sim/out/pv_tradeoff/fronts.png

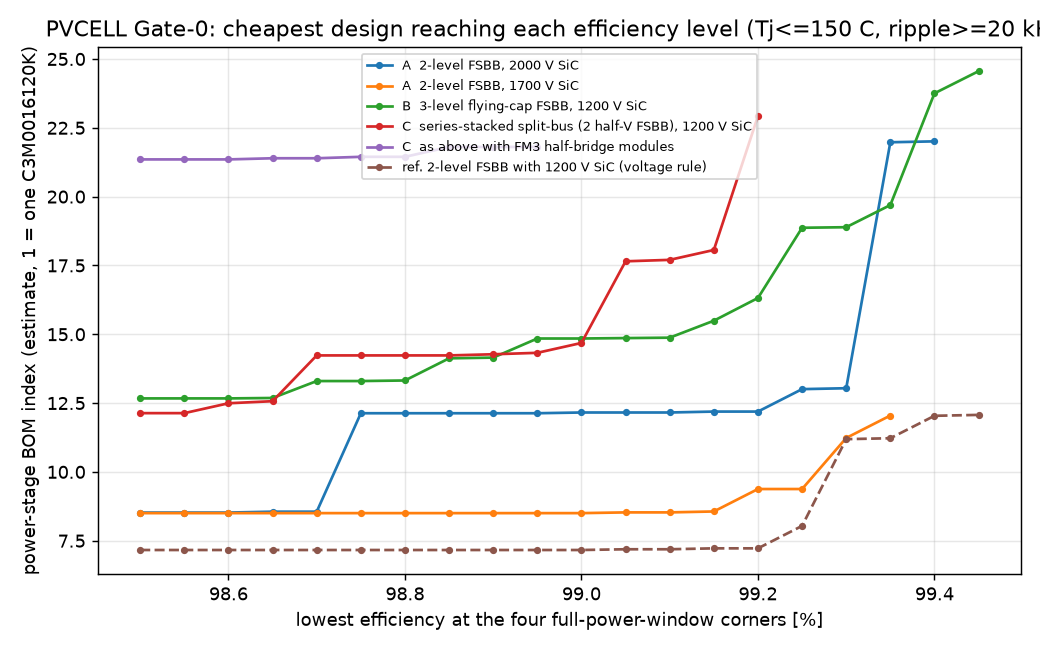
sim/out/pv_tradeoff/fronts.png
