vectivolt/PCM/sim/out/pv_tradeoff/loss_breakdown.png

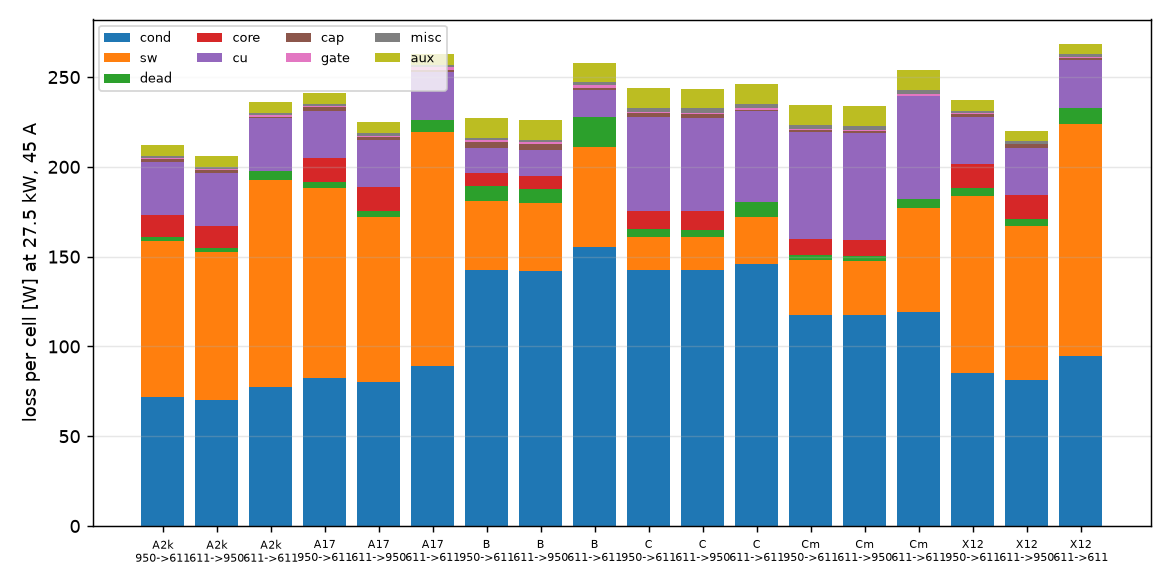
sim/out/pv_tradeoff/loss_breakdown.png
