vectivolt/PCM/sim/out/pv_tradeoff/transition_sweep.png

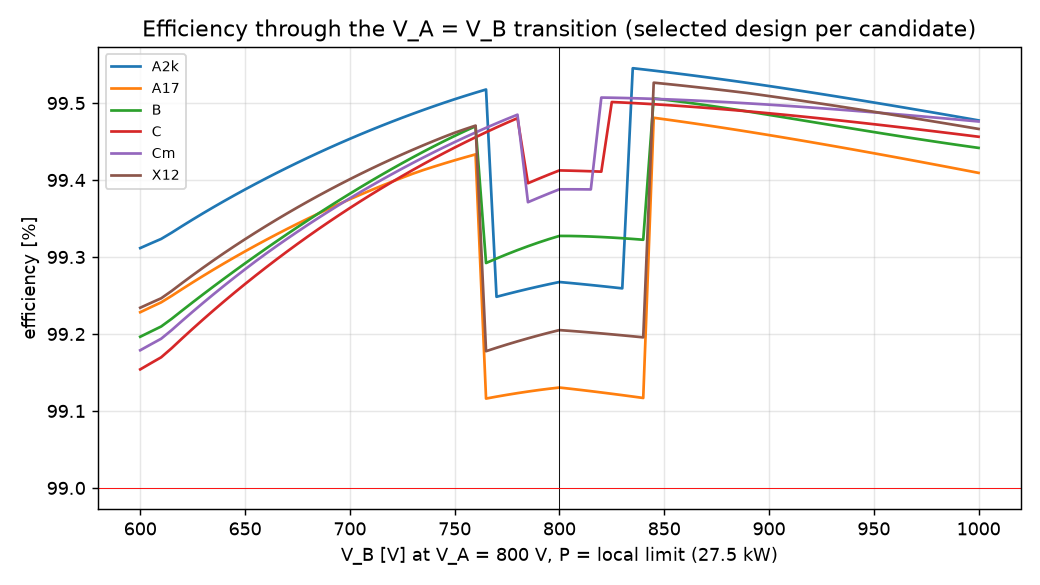
sim/out/pv_tradeoff/transition_sweep.png
