vectivolt/PCM/bom/DAB-D60-FULL_costed_BOM.csv

Item | Qty | Used on | Value | Description | Manufacturer | MPN | Package | Sourcing | Datasheet | unit_cost_usd | ext_cost_usd | price_source | confidence | unit_cost_5k_usd | basis_5k
1 | 1 | DAB60: 1 | 2.12 uH series L (CUSTOM) | CUSTOM series inductor (COLD-PLATE MOUNTED), primary (port-1) side, in series with the transformer: L 2.12 uH nominal, trim 1.24-2.99 uH so that leakage + L = 6.50 uH +/-5 % (leakage + external, measured as a matched set); I_rms 118.5 A, I_pk 176.9 A, no saturation to 275 A; loss <= 11.2 W; reference PM 114/93 N95, 3 turns, 9.2 mm total gap in >=4 distributed gaps |  |  | cold-plate mounted | CUSTOM |  | 86.000000 | 86.0000 | estimate 2.12 uH series L (CUSTOM): ESTIMATE (sim/magnetics.py design_dab_series_inductor.json rev M1; the value becomes 5.56 uH): 4 x DMEGC EE80 DMR95 + gapped centre-leg s... | low | 73.100000 | ASSUMED x0.85 [custom_magnetic_large]
2 | 1 | chassis: 1 | AUX-HV input harness | PORT 1 ONLY: port-1 terminal-side tap to AUX-HV PA+/PA-, 1.5 kV-rated wire. AUX-HV input PB is left open - feeding it from port 2 as well would bridge the DAB's isolation barrier with two diodes (decision D-021) |  |  | harness | CUSTOM |  | 5.000000 | 5.0000 | estimate AUX-HV input harness: ESTIMATE: two port taps, 1.5 kV-rated silicone wire 0.8 m 1.8 + 2 ring lugs 0.8 + 4-pole plug 0.6 + assembly 1.8; no quote | low | 4.000000 | ASSUMED x0.80 [custom_harness]
3 | 1 | chassis: 1 | AUX-HV output harness | AUX-HV to SYS-IO-AUX, 3-way (gen/interfaces.py AUX) |  |  | harness | CUSTOM |  | 1.800000 | 1.8000 | estimate AUX-HV output harness: ESTIMATE: 3-way plug-to-plug harness 0.4 m: 2 plugs 0.35 each + wire 0.3 + assembly 0.8; no quote | low | 1.440000 | ASSUMED x0.80 [custom_harness]
4 | 2 | DAB60: 2 | CM choke 160 A (CUSTOM) | CHASSIS-MOUNTED CUSTOM common-mode choke (135 A port): 2 windings, 160 A DC continuous each, 1000 VDC working, L_cm >= 0.5 mH @ 10 kHz and |Z_cm| >= 50 ohm 16-100 kHz (port_spec cm_choke), no saturation with the 150 Hz CM current of port_spec cm_choke and the DM flux at rated current (core, material and construction to be set by the magnetics design, MG-10); basic winding-core / winding-winding: impulse >= 6 kV, 2200 V rms 60 s, creepage >= 5.0 mm (PD2) (IC-09); dT <= 40 K at 160 A |  |  | busbar toroid | CUSTOM |  | 65.000000 | 130.0000 | estimate CM choke 160 A (CUSTOM): ESTIMATE: nanocrystalline toroid about 0.6 kg finished core 35 + two 160 A copper windings (about 0.3 kg Cu, 4.5 USD at LME copper cash 1... | low | 55.250000 | ASSUMED x0.85 [custom_magnetic_large]
5 | 2 | DAB60: 2 | DC terminal + (CUSTOM) | CHASSIS-MOUNTED CUSTOM DC terminal: M8 busbar stud feed-through, 200 A, 1000 VDC, touch cover, external creepage to PE >= 12.5 mm (group I) / 16.0 mm (IIIa), PD3 cooling-air path (IC-18/IC-21) |  |  | M8 stud | CUSTOM |  | 8.000000 | 16.0000 | estimate DC terminal + (CUSTOM): ESTIMATE: M8 copper stud feed-through 200 A with insulating body and touch cover; no quote or listing found | low | 6.800000 | ASSUMED x0.85 [custom_mech]
6 | 2 | DAB60: 2 | DC terminal - (CUSTOM) | CHASSIS-MOUNTED CUSTOM DC terminal: M8 busbar stud feed-through, 200 A, 1000 VDC, touch cover, external creepage to PE >= 12.5 mm (group I) / 16.0 mm (IIIa), PD3 cooling-air path (IC-18/IC-21) |  |  | M8 stud | CUSTOM |  | 8.000000 | 16.0000 | estimate DC terminal - (CUSTOM): ESTIMATE: as DC terminal + | low | 6.800000 | ASSUMED x0.85 [custom_mech]
7 | 1 | DAB60: 1 | DC-block link (CUSTOM) | CUSTOM bolted busbar link in the primary AC bus, FITTED: bolted link in the primary AC bus so a blocking-cap module can be added. Remove to insert the DC-blocking capacitor module (5 x C4AQUEW5450A3BJ (225 uF), not fitted; C_min 39 uF by the TI rule, 8.7 W) |  |  | bolted busbar link | CUSTOM |  | 7.000000 | 7.0000 | estimate DC-block link (CUSTOM): ESTIMATE: bolted tinned copper link about 20x5x150 mm = 0.13 kg Cu (1.9 at LME copper cash 14,355 USD/t on 2026-10-02 (westmetall.com)) +... | low | 5.950000 | ASSUMED x0.85 [custom_magnetic_large]
8 | 1 | DAB60: 1 | Transformer 11:12 (CUSTOM) | CUSTOM HF power transformer (COLD-PLATE MOUNTED), N1:N2 = 11:12 (n 0.9167); L_sigma 4.38 uH +/-20 % (design target, referred to N1); L_m 150 uH +/-10 % (gapped, ~1.74 mm total); 4.75 mVs per half period, B_pk 126 mT at 950 V; I_rms 118.5 / 111.9 A, I_pk 176.9 / 162.1 A (prim / sec); loss <= 159 W; hot spot <= 130 C (coolant 50 C); insulation basic (pending system decision), working-voltage basis 1850 V DC, PD <= 10 pC at the ECO-10 level (hipot/PD: TBD by ECO-10 insulation coordination); reference core TDK PM 114/93 N95 (B65733A0000R095 ground to gap) + bobbin B65734B1000T001 - reference only; embedded NTC 10 k +/-2 %, R/T 8016 (B25/100 3988 K, as TDK B57703M0103) at the winding hot spot, leads TH1/TH2 reinforced to PELV. Full RFQ: sim/out/dab_design/report.md sec. 9 |  |  | cold-plate mounted, PM 114/93 class | CUSTOM |  | 186.000000 | 186.0000 | estimate Transformer 11:12 (CUSTOM): ESTIMATE (sim/magnetics.py design_dab_transformer.json rev M1): pair of potted units, 4 x DMEGC EE80 DMR95 (2.96 kg at 6.0 USD/kg) + litz... | low | 158.100000 | ASSUMED x0.85 [custom_magnetic_large]
9 | 2 | chassis: 2 | cell harness | 40-way 2.54 mm IDC ribbon, CTRL-C2000 ports C1 and C2 to the DAB60 bridges, 1:1 |  |  | harness | CUSTOM |  | 2.400000 | 4.8000 | estimate cell harness: ESTIMATE: 40-way 2.54 mm IDC ribbon assembly: 2 IDC sockets 0.45 each + 0.4 m ribbon 0.5 + assembly 1.0; connector prices are the LCSC cl... | low | 1.920000 | ASSUMED x0.80 [custom_harness]
10 | 1 | chassis: 1 | coil/feedback harness | DAB60 control connector to the SYS-IO-AUX DO/DI terminals |  |  | harness | CUSTOM |  | 5.500000 | 5.5000 | estimate coil/feedback harness: ESTIMATE: 14-way pluggable header mate 1.8 + 0.6 m multicore with ferrules 1.5 + assembly 2.2; no quote | low | 4.400000 | ASSUMED x0.80 [custom_harness]
11 | 1 | chassis: 1 | cold plate | Liquid cold plate for two CBB011M12GM4T modules, transformer and series inductor; 0.045 K/W per switch position at 9 L/min - sim/out/dab_design/report.md section 12 |  |  | chassis | CUSTOM |  | 120.000000 | 120.0000 | estimate cold plate: ESTIMATE: friction-stir-welded aluminium liquid cold plate, about 350x200 mm for two GM4 modules + PM114 transformer + series inductor, t... | low | 102.000000 | ASSUMED x0.85 [custom_mech]
12 | 1 | chassis: 1 | port harness | 26-way 2.54 mm IDC ribbon, CTRL-C2000 to DAB60, 1:1 |  |  | harness | CUSTOM |  | 1.900000 | 1.9000 | estimate port harness: ESTIMATE: 26-way 2.54 mm IDC ribbon assembly: 2 IDC sockets 0.35 each + ribbon 0.35 + assembly 0.85; no quote | low | 1.520000 | ASSUMED x0.80 [custom_harness]
13 | 1 | AUX-HV_DAB: 1 | AUX-HV-T1 rev M1 | CUSTOM flyback transformer AUX-HV T1 rev M1 (proposed construction - calculated, not built or measured; build to the winding sheet sim/out/magnetics/spec_aux_hv_transformer.md). DMEGC EC34A (ETD 34/17/11 class) DMR95, centre-leg gap 1.16 mm, 90:15:16 in the converter engineer's order P1|SH|S|AUX|P2, copper set back 2.0 mm from the gapped leg (1.0 mm former wall + 1.0 mm spacer), secondary in TIW-litz, vacuum-potted in a case. Core DMEGC EC34A set (DMR95), ETD 34/17/11 equivalent (Ae/Amin/le within 1 % of the MAS ETD 34/17/11 shape), gap 1.16 mm (A_L 142 nH). Lp 1.148 mH +/-7 % at 10 kHz (gap ground to A_L); leakage (S shorted) estimate 31.6 uH, <= 34.0 uH. Windings in order: P1: 45 t enamelled Cu 0.30 mm grade 2, 1 layer, start = DRAIN pin (dot); SH: copper foil 0.05 mm, 1 t, open with insulated overlap, -> PGND pin; S: 15 t TIW-litz 64 x 0.10 mm (three-layer extruded insulation certified for reinforced insulation, IEC 61558-2-16 / IEC 62368-1 Annex J), 1 layer, start = rectifier anode (dot), insulation unbroken to the pin, exits in PTFE sleeve; AUX: 16 t enamelled Cu 0.25 mm spaced over the breadth, start = aux rectifier anode (dot), finish = PGND; P2: 45 t enamelled Cu 0.30 mm grade 2, 1 layer, finish = HV_BULK pin. Insulation: VACUUM-POTTED (epoxy, class F, void-free) in a case - REQUIRED for the PD routine test; reinforced insulation = TIW-litz three-layer extruded insulation + 4 layers 0.06 mm polyester tape on each side of S; tapes P1-SH 12 L set the switched capacita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 | CUSTOM | AUX-HV-T1 rev M1 | DMEGC EC34A set (DMR95) (ETD 34 class) potted case, 14-pin former | CUSTOM |  | 5.900000 | 5.9000 | estimate AUX-HV-T1 rev M1: ESTIMATE (sim/magnetics.py design_aux_hv_transformer.json rev M1): DMEGC EC34A DMR95 0.40 + ETD34 former 0.35 + TIW-litz 1.20 + wire/foil... | low | 3.953000 | ASSUMED x0.67 [custom_magnetic_small]
14 | 8 | DAB60: 8 | 0.27R | Resistor 0.27R 1% 2512 Roff, pulse-rated thick film 1 W |  |  | 2512 | GENERIC |  | 0.147800 | 1.1824 | estimate class:res_2512_1pct_pulse: GENERIC class rule, reel price of a typical equivalent. LCSC C2991665 RPL-12K10R0FT (2512); US$0.1478 at 4000+; pulse-rated 2512 thick fi... | low | 0.147800 | REAL: class example LCSC C2991665 @4000+ break (annual qty 40000)
15 | 2 | DAB60: 2 | 0R | Resistor 0R 1% 0805 HV-side sensor ground: single Kelvin tie to the bank DC- terminal |  |  | 0805 | GENERIC |  | 0.001500 | 0.0030 | estimate class:res_0805_1pct: GENERIC class rule, reel price of a typical equivalent. LCSC C17878 0805W8F976JT5E (0805); US$0.0015 at 5000+; 97.6 Ohm 1 %; read 2026-10... | high | 0.001400 | REAL: class example LCSC C17878 @10000+ break (annual qty 10000)
16 | 1 | DAB60: 1 | 0R | Resistor 0R 1% 0603 single AGND-GND tie |  |  | 0603 | GENERIC |  | 0.003000 | 0.0030 | estimate class:res_0603_1pct: GENERIC class rule, reel price of a typical equivalent. LCSC C2906982 FRC0603F1002TS (0603); US$0.003 at 5000+; 10 kOhm 1 %; read 2026-10... | high | 0.003000 | REAL: class example LCSC C2906982 @5000+ break (annual qty 5000)
17 | 2 | DAB60: 2 | 1.07k | Resistor 1.07k 1% 0603 |  |  | 0603 | GENERIC |  | 0.003000 | 0.0060 | estimate class:res_0603_1pct: GENERIC class rule, reel price of a typical equivalent. LCSC C2906982 FRC0603F1002TS (0603); US$0.003 at 5000+; 10 kOhm 1 %; read 2026-10... | high | 0.002900 | REAL: class example LCSC C2906982 @10000+ break (annual qty 10000)
18 | 1 | CTRL-C2000: 1 | 1.0k | Resistor 1.0k 1% 0603 |  |  | 0603 | GENERIC |  | 0.003000 | 0.0030 | estimate class:res_0603_1pct: GENERIC class rule, reel price of a typical equivalent. LCSC C2906982 FRC0603F1002TS (0603); US$0.003 at 5000+; 10 kOhm 1 %; read 2026-10... | high | 0.003000 | REAL: class example LCSC C2906982 @5000+ break (annual qty 5000)
19 | 24 | CTRL-C2000: 24 | 1.50k | Resistor 1.50k 1% 0603 |  |  | 0603 | GENERIC |  | 0.003000 | 0.0720 | estimate class:res_0603_1pct: GENERIC class rule, reel price of a typical equivalent. LCSC C2906982 FRC0603F1002TS (0603); US$0.003 at 5000+; 10 kOhm 1 %; read 2026-10... | high | 0.002800 | REAL: class example LCSC C2906982 @50200+ break (annual qty 120000)
20 | 4 | DAB60: 4 | 1.56k | Resistor 1.56k 0.1% 0603 |  |  | 0603 | GENERIC |  | 0.003900 | 0.0156 | estimate class:res_0603_0.1pct: GENERIC class rule, reel price of a typical equivalent. LCSC C5126214 FRH0603B1002TS (0603); US$0.0039 at 5000+; 10 kOhm 0.1 %; read 2026... | high | 0.003500 | REAL: class example LCSC C5126214 @10000+ break (annual qty 20000)
21 | 2 | AUX-HV_DAB: 2 | 1.5R | Resistor 1.5R 1% 1206 0.25 W |  |  | 1206 | GENERIC |  | 0.002300 | 0.0046 | estimate class:res_1206_1pct: GENERIC class rule, reel price of a typical equivalent. LCSC C305316 WR12X1581FTL (1206); US$0.0023 at 5000+; 1.58 kOhm 1 %; read 2026-10... | high | 0.002100 | REAL: class example LCSC C305316 @10000+ break (annual qty 10000)
22 | 2 | DAB60: 2 | 1.5k | Resistor 1.5k 1% 2512 1 W: aux wetting 14-18 mA (>= 10 mA, TDK p3) and FB inversion |  |  | 2512 | GENERIC |  | 0.025800 | 0.0516 | estimate class:res_2512_1pct: GENERIC class rule, reel price of a typical equivalent. LCSC C2934076 FRC2512F4702TS (2512); US$0.0258 at 4000+; 47 kOhm 1 W 1 %; read 20... | high | 0.024100 | REAL: class example LCSC C2934076 @8000+ break (annual qty 10000)
23 | 1 | AUX-HV_DAB: 1 | 1.5n 50V | Capacitor 1.5n 50V C0G 0603 |  |  | 0603 | GENERIC |  | 0.028200 | 0.0282 | estimate class:mlcc_0603_c0g_50v_le100n: GENERIC class rule, reel price of a typical equivalent. LCSC C576818 CC0603JRNPO9BN472 (0603); US$0.0282 at 4000+; example is 4.7 nF; rea... | high | 0.028200 | REAL: class example LCSC C576818 @4000+ break (annual qty 5000)
24 | 2 | DAB60: 2 | 1.69k | Resistor 1.69k 0.1% 0603 |  |  | 0603 | GENERIC |  | 0.003900 | 0.0078 | estimate class:res_0603_0.1pct: GENERIC class rule, reel price of a typical equivalent. LCSC C5126214 FRH0603B1002TS (0603); US$0.0039 at 5000+; 10 kOhm 0.1 %; read 2026... | high | 0.003500 | REAL: class example LCSC C5126214 @10000+ break (annual qty 10000)
25 | 4 | DAB60: 4 | 1.6M | Resistor 1.6M 0.1% 0603 |  |  | 0603 | GENERIC |  | 0.003900 | 0.0156 | estimate class:res_0603_0.1pct: GENERIC class rule, reel price of a typical equivalent. LCSC C5126214 FRH0603B1002TS (0603); US$0.0039 at 5000+; 10 kOhm 0.1 %; read 2026... | high | 0.003500 | REAL: class example LCSC C5126214 @10000+ break (annual qty 20000)
26 | 1 | SYS-IO-AUX: 1 | 1.78k | Resistor 1.78k 0.1% 0603 10 ppm/K thin film |  |  | 0603 | GENERIC |  | 0.041000 | 0.0410 | estimate class:res_0603_0.1pct_10ppm: GENERIC class rule, reel price of a typical equivalent. LCSC C190610 ERA3AEB103V (0603); US$0.041 at 5000+; Panasonic ERA-3A thin film 0.... | medium | 0.041000 | REAL: class example LCSC C190610 @5000+ break (annual qty 5000)
27 | 1 | AUX-HV_DAB: 1 | 1.82k | Resistor 1.82k 0.1% 0603 |  |  | 0603 | GENERIC |  | 0.003900 | 0.0039 | estimate class:res_0603_0.1pct: GENERIC class rule, reel price of a typical equivalent. LCSC C5126214 FRH0603B1002TS (0603); US$0.0039 at 5000+; 10 kOhm 0.1 %; read 2026... | high | 0.003900 | REAL: class example LCSC C5126214 @5000+ break (annual qty 5000)
28 | 8 | DAB60: 8 | 1.82k | Resistor 1.82k 1% 0805 |  |  | 0805 | GENERIC |  | 0.001500 | 0.0120 | estimate class:res_0805_1pct: GENERIC class rule, reel price of a typical equivalent. LCSC C17878 0805W8F976JT5E (0805); US$0.0015 at 5000+; 97.6 Ohm 1 %; read 2026-10... | high | 0.001400 | REAL: class example LCSC C17878 @10000+ break (annual qty 40000)
29 | 8 | DAB60: 8 | 1.87k | Resistor 1.87k 1% 0603 |  |  | 0603 | GENERIC |  | 0.003000 | 0.0240 | estimate class:res_0603_1pct: GENERIC class rule, reel price of a typical equivalent. LCSC C2906982 FRC0603F1002TS (0603); US$0.003 at 5000+; 10 kOhm 1 %; read 2026-10... | high | 0.002900 | REAL: class example LCSC C2906982 @10000+ break (annual qty 40000)
30 | 1 | SYS-IO-AUX: 1 | 1.91k | Resistor 1.91k 0.1% 0603 10 ppm/K thin film |  |  | 0603 | GENERIC |  | 0.041000 | 0.0410 | estimate class:res_0603_0.1pct_10ppm: GENERIC class rule, reel price of a typical equivalent. LCSC C190610 ERA3AEB103V (0603); US$0.041 at 5000+; Panasonic ERA-3A thin film 0.... | medium | 0.041000 | REAL: class example LCSC C190610 @5000+ break (annual qty 5000)
31 | 2 | SYS-IO-AUX: 2 | 1.93k | Resistor 1.93k 0.1% 0603 10 ppm/K thin film |  |  | 0603 | GENERIC |  | 0.041000 | 0.0820 | estimate class:res_0603_0.1pct_10ppm: GENERIC class rule, reel price of a typical equivalent. LCSC C190610 ERA3AEB103V (0603); US$0.041 at 5000+; Panasonic ERA-3A thin film 0.... | medium | 0.038900 | REAL: class example LCSC C190610 @10000+ break (annual qty 10000)
32 | 4 | DAB60: 4 | 1.96k | Resistor 1.96k 0.1% 0603 |  |  | 0603 | GENERIC |  | 0.003900 | 0.0156 | estimate class:res_0603_0.1pct: GENERIC class rule, reel price of a typical equivalent. LCSC C5126214 FRH0603B1002TS (0603); US$0.0039 at 5000+; 10 kOhm 0.1 %; read 2026... | high | 0.003500 | REAL: class example LCSC C5126214 @10000+ break (annual qty 20000)
33 | 46 | CTRL-C2000: 46 | 10.0k | Resistor 10.0k 0.1% 0603 10ppm/K |  |  | 0603 | GENERIC |  | 0.041000 | 1.8860 | estimate class:res_0603_0.1pct_10ppm: GENERIC class rule, reel price of a typical equivalent. LCSC C190610 ERA3AEB103V (0603); US$0.041 at 5000+; Panasonic ERA-3A thin film 0.... | medium | 0.038900 | REAL: class example LCSC C190610 @10000+ break (annual qty 230000)
34 | 6 | CTRL-C2000: 6 | 10.0k | Resistor 10.0k 0.1% 0603 |  |  | 0603 | GENERIC |  | 0.003900 | 0.0234 | estimate class:res_0603_0.1pct: GENERIC class rule, reel price of a typical equivalent. LCSC C5126214 FRH0603B1002TS (0603); US$0.0039 at 5000+; 10 kOhm 0.1 %; read 2026... | high | 0.003500 | REAL: class example LCSC C5126214 @10000+ break (annual qty 30000)
35 | 3 | CTRL-C2000: 1; DAB60: 2 | 10.0k | Resistor 10.0k 1% 0603 |  |  | 0603 | GENERIC |  | 0.003000 | 0.0090 | estimate class:res_0603_1pct: GENERIC class rule, reel price of a typical equivalent. LCSC C2906982 FRC0603F1002TS (0603); US$0.003 at 5000+; 10 kOhm 1 %; read 2026-10... | high | 0.002900 | REAL: class example LCSC C2906982 @10000+ break (annual qty 15000)
36 | 30 | CTRL-C2000: 3; DAB60: 18; SYS-IO-AUX: 9 | 100R | Resistor 100R 1% 0603 |  |  | 0603 | GENERIC |  | 0.003000 | 0.0900 | estimate class:res_0603_1pct: GENERIC class rule, reel price of a typical equivalent. LCSC C2906982 FRC0603F1002TS (0603); US$0.003 at 5000+; 10 kOhm 1 %; read 2026-10... | high | 0.002800 | REAL: class example LCSC C2906982 @50200+ break (annual qty 150000)
37 | 2 | DAB60: 2 | 100R | Resistor 100R 1% 0603 RDY driven actively (CTRL 100k pull-down) |  |  | 0603 | GENERIC |  | 0.003000 | 0.0060 | estimate class:res_0603_1pct: GENERIC class rule, reel price of a typical equivalent. LCSC C2906982 FRC0603F1002TS (0603); US$0.003 at 5000+; 10 kOhm 1 %; read 2026-10... | high | 0.002900 | REAL: class example LCSC C2906982 @10000+ break (annual qty 10000)
38 | 67 | AUX-HV_DAB: 4; CTRL-C2000: 28; DAB60: 11; SYS-IO-AUX: 24 | 100k | Resistor 100k 1% 0603 |  |  | 0603 | GENERIC |  | 0.003000 | 0.2010 | estimate class:res_0603_1pct: GENERIC class rule, reel price of a typical equivalent. LCSC C2906982 FRC0603F1002TS (0603); US$0.003 at 5000+; 10 kOhm 1 %; read 2026-10... | high | 0.002800 | REAL: class example LCSC C2906982 @50200+ break (annual qty 335000)
39 | 6 | SYS-IO-AUX: 6 | 100k | Resistor 100k 0.1% 0603 10 ppm/K thin film |  |  | 0603 | GENERIC |  | 0.041000 | 0.2460 | estimate class:res_0603_0.1pct_10ppm: GENERIC class rule, reel price of a typical equivalent. LCSC C190610 ERA3AEB103V (0603); US$0.041 at 5000+; Panasonic ERA-3A thin film 0.... | medium | 0.038900 | REAL: class example LCSC C190610 @10000+ break (annual qty 30000)
40 | 7 | DAB60: 6; SYS-IO-AUX: 1 | 100k | Resistor 100k 0.1% 0603 |  |  | 0603 | GENERIC |  | 0.003900 | 0.0273 | estimate class:res_0603_0.1pct: GENERIC class rule, reel price of a typical equivalent. LCSC C5126214 FRH0603B1002TS (0603); US$0.0039 at 5000+; 10 kOhm 0.1 %; read 2026... | high | 0.003500 | REAL: class example LCSC C5126214 @10000+ break (annual qty 35000)
41 | 3 | SYS-IO-AUX: 3 | 100k | Resistor 100k 1% 0603 test off by default |  |  | 0603 | GENERIC |  | 0.003000 | 0.0090 | estimate class:res_0603_1pct: GENERIC class rule, reel price of a typical equivalent. LCSC C2906982 FRC0603F1002TS (0603); US$0.003 at 5000+; 10 kOhm 1 %; read 2026-10... | high | 0.002900 | REAL: class example LCSC C2906982 @10000+ break (annual qty 15000)
42 | 2 | SYS-IO-AUX: 2 | 100k | Resistor 100k 1% 0603 CTRL expects the pull-down on SYS |  |  | 0603 | GENERIC |  | 0.003000 | 0.0060 | estimate class:res_0603_1pct: GENERIC class rule, reel price of a typical equivalent. LCSC C2906982 FRC0603F1002TS (0603); US$0.003 at 5000+; 10 kOhm 1 %; read 2026-10... | high | 0.002900 | REAL: class example LCSC C2906982 @10000+ break (annual qty 10000)
43 | 1 | SYS-IO-AUX: 1 | 100k | Resistor 100k 1% 0603 fans OFF until firmware enables (INT-09) |  |  | 0603 | GENERIC |  | 0.003000 | 0.0030 | estimate class:res_0603_1pct: GENERIC class rule, reel price of a typical equivalent. LCSC C2906982 FRC0603F1002TS (0603); US$0.003 at 5000+; 10 kOhm 1 %; read 2026-10... | high | 0.003000 | REAL: class example LCSC C2906982 @5000+ break (annual qty 5000)
44 | 1 | SYS-IO-AUX: 1 | 100k | Resistor 100k 1% 0603 readback cannot hold OV_CUT |  |  | 0603 | GENERIC |  | 0.003000 | 0.0030 | estimate class:res_0603_1pct: GENERIC class rule, reel price of a typical equivalent. LCSC C2906982 FRC0603F1002TS (0603); US$0.003 at 5000+; 10 kOhm 1 %; read 2026-10... | high | 0.003000 | REAL: class example LCSC C2906982 @5000+ break (annual qty 5000)
45 | 1 | SYS-IO-AUX: 1 | 100k | Resistor 100k 1% 0603 readback cannot hold UV_OK |  |  | 0603 | GENERIC |  | 0.003000 | 0.0030 | estimate class:res_0603_1pct: GENERIC class rule, reel price of a typical equivalent. LCSC C2906982 FRC0603F1002TS (0603); US$0.003 at 5000+; 10 kOhm 1 %; read 2026-10... | high | 0.003000 | REAL: class example LCSC C2906982 @5000+ break (annual qty 5000)
46 | 1 | SYS-IO-AUX: 1 | 100k | Resistor 100k 1% 0603 service-jumper readback |  |  | 0603 | GENERIC |  | 0.003000 | 0.0030 | estimate class:res_0603_1pct: GENERIC class rule, reel price of a typical equivalent. LCSC C2906982 FRC0603F1002TS (0603); US$0.003 at 5000+; 10 kOhm 1 %; read 2026-10... | high | 0.003000 | REAL: class example LCSC C2906982 @5000+ break (annual qty 5000)
47 | 1 | SYS-IO-AUX: 1 | 100k | Resistor 100k 1% 0603 readback cannot hold AUX_INH_N |  |  | 0603 | GENERIC |  | 0.003000 | 0.0030 | estimate class:res_0603_1pct: GENERIC class rule, reel price of a typical equivalent. LCSC C2906982 FRC0603F1002TS (0603); US$0.003 at 5000+; 10 kOhm 1 %; read 2026-10... | high | 0.003000 | REAL: class example LCSC C2906982 @5000+ break (annual qty 5000)
48 | 2 | DAB60: 2 | 100k | Resistor 100k 1% 0603 gate pull-down: off when the driver is unpowered |  |  | 0603 | GENERIC |  | 0.003000 | 0.0060 | estimate class:res_0603_1pct: GENERIC class rule, reel price of a typical equivalent. LCSC C2906982 FRC0603F1002TS (0603); US$0.003 at 5000+; 10 kOhm 1 %; read 2026-10... | high | 0.002900 | REAL: class example LCSC C2906982 @10000+ break (annual qty 10000)
49 | 2 | DAB60: 2 | 100k | Resistor 100k 1% 0603 EN pull-down behind the diode-OR |  |  | 0603 | GENERIC |  | 0.003000 | 0.0060 | estimate class:res_0603_1pct: GENERIC class rule, reel price of a typical equivalent. LCSC C2906982 FRC0603F1002TS (0603); US$0.003 at 5000+; 10 kOhm 1 %; read 2026-10... | high | 0.002900 | REAL: class example LCSC C2906982 @10000+ break (annual qty 10000)
50 | 4 | DAB60: 4 | 100k | Resistor 100k 1% 0603 FB 24 V -> logic, max 5.4 V (5.5 V tolerant) |  |  | 0603 | GENERIC |  | 0.003000 | 0.0120 | estimate class:res_0603_1pct: GENERIC class rule, reel price of a typical equivalent. LCSC C2906982 FRC0603F1002TS (0603); US$0.003 at 5000+; 10 kOhm 1 %; read 2026-10... | high | 0.002900 | REAL: class example LCSC C2906982 @10000+ break (annual qty 20000)
51 | 4 | DAB60: 4 | 100k | Resistor 100k 1% 0603 hold off while the logic is unpowered |  |  | 0603 | GENERIC |  | 0.003000 | 0.0120 | estimate class:res_0603_1pct: GENERIC class rule, reel price of a typical equivalent. LCSC C2906982 FRC0603F1002TS (0603); US$0.003 at 5000+; 10 kOhm 1 %; read 2026-10... | high | 0.002900 | REAL: class example LCSC C2906982 @10000+ break (annual qty 20000)
52 | 19 | CTRL-C2000: 6; SYS-IO-AUX: 13 | 100n 100V | Capacitor 100n 100V X7R 0603 |  |  | 0603 | GENERIC |  | 0.011100 | 0.2109 | estimate class:mlcc_0603_x7r_100v_le100n: GENERIC class rule, reel price of a typical equivalent. LCSC C113803 CC0603KRX7R0BB104 (0603); US$0.0111 at 4000+; read 2026-10-04 via th... | high | 0.010500 | REAL: class example LCSC C113803 @48000+ break (annual qty 95000)
53 | 34 | CTRL-C2000: 34 | 100n 16V | Capacitor 100n 16V X7R 0402 |  |  | 0402 | GENERIC |  | 0.004700 | 0.1598 | estimate class:mlcc_0402_x7r_16v_le100n: GENERIC class rule, reel price of a typical equivalent. LCSC C1525 CL05B104KO5NNNC (0402); US$0.0047 at 3000+; read 2026-10-04 via the jl... | high | 0.004200 | REAL: class example LCSC C1525 @100000+ break (annual qty 170000)
54 | 5 | AUX-HV_DAB: 1; SYS-IO-AUX: 4 | 100n 16V | Capacitor 100n 16V X7R 0603 |  |  | 0603 | GENERIC |  | 0.009200 | 0.0460 | estimate class:mlcc_0603_x7r_16v_le100n: GENERIC class rule, reel price of a typical equivalent. LCSC C14663 CC0603KRX7R9BB104 (0603); US$0.0092 at 4000+; example is rated 50 V (... | high | 0.009000 | REAL: class example LCSC C14663 @24100+ break (annual qty 25000)
55 | 7 | DAB60: 4; SYS-IO-AUX: 3 | 100n 25V | Capacitor 100n 25V X7R 0603 |  |  | 0603 | GENERIC |  | 0.009200 | 0.0644 | estimate class:mlcc_0603_x7r_25v_le100n: GENERIC class rule, reel price of a typical equivalent. LCSC C14663 CC0603KRX7R9BB104 (0603); US$0.0092 at 4000+; example is rated 50 V;... | high | 0.009000 | REAL: class example LCSC C14663 @24100+ break (annual qty 35000)
56 | 289 | AUX-HV_DAB: 3; BMU-GW: 7; CTRL-C2000: 49; DAB60: 154; SYS-IO-AUX: 76 | 100n 50V | Capacitor 100n 50V X7R 0603 |  |  | 0603 | GENERIC |  | 0.009200 | 2.6588 | estimate class:mlcc_0603_x7r_50v_le100n: GENERIC class rule, reel price of a typical equivalent. LCSC C14663 CC0603KRX7R9BB104 (0603); US$0.0092 at 4000+; read 2026-10-04 via the... | high | 0.009000 | REAL: class example LCSC C14663 @24100+ break (annual qty 1445000)
57 | 1 | CTRL-C2000: 1 | 100n 50V | Capacitor 100n 5% 50V C0G 0805 |  |  | 0805 | GENERIC |  | 0.136200 | 0.1362 | estimate class:mlcc_0805_c0g_50v_le100n: GENERIC class rule, reel price of a typical equivalent. LCSC C97946 GRM31C5C1H104JA01L (1206); US$0.1362 at 4000+; no 0805 C0G >= 10 nF i... | low | 0.136200 | REAL: class example LCSC C97946 @4000+ break (annual qty 5000)
58 | 2 | CTRL-C2000: 1; SYS-IO-AUX: 1 | 100n 50V | Capacitor 100n 10% 50V X7R 0603 |  |  | 0603 | GENERIC |  | 0.009200 | 0.0184 | estimate class:mlcc_0603_x7r_50v_le100n: GENERIC class rule, reel price of a typical equivalent. LCSC C14663 CC0603KRX7R9BB104 (0603); US$0.0092 at 4000+; read 2026-10-04 via the... | high | 0.009200 | REAL: class example LCSC C14663 @4000+ break (annual qty 10000)
59 | 8 | DAB60: 8 | 100n 50V | Capacitor 100n 50V C0G 1206 |  |  | 1206 | GENERIC |  | 0.136200 | 1.0896 | estimate class:mlcc_1206_c0g_50v_le100n: GENERIC class rule, reel price of a typical equivalent. LCSC C97946 GRM31C5C1H104JA01L (1206); US$0.1362 at 4000+; example is 100 nF 50 V... | high | 0.136200 | REAL: class example LCSC C97946 @4000+ break (annual qty 40000)
60 | 3 | AUX-HV_DAB: 3 | 100p 1kV | Capacitor 100p 5% 1kV C0G 1206 |  |  | 1206 | GENERIC |  | 0.025300 | 0.0759 | estimate class:mlcc_1206_c0g_1kv_le1n: GENERIC class rule, reel price of a typical equivalent. LCSC C107173 CC1206JKNPOCBN101 (1206); US$0.0253 at 3000+; example is 100 pF 1 kV... | high | 0.024000 | REAL: class example LCSC C107173 @6000+ break (annual qty 15000)
61 | 48 | DAB60: 48 | 100p 50V | Capacitor 100p 5% 50V C0G 0603 |  |  | 0603 | GENERIC |  | 0.005500 | 0.2640 | estimate class:mlcc_0603_c0g_50v_le1n: GENERIC class rule, reel price of a typical equivalent. LCSC C14665 CC0603JRNPO9BN101 (0603); US$0.0055 at 4000+; example is 100 pF; read... | high | 0.005100 | REAL: class example LCSC C14665 @48200+ break (annual qty 240000)
62 | 2 | DAB60: 2 | 102k | Resistor 102k 0.1% 0603 |  |  | 0603 | GENERIC |  | 0.003900 | 0.0078 | estimate class:res_0603_0.1pct: GENERIC class rule, reel price of a typical equivalent. LCSC C5126214 FRH0603B1002TS (0603); US$0.0039 at 5000+; 10 kOhm 0.1 %; read 2026... | high | 0.003500 | REAL: class example LCSC C5126214 @10000+ break (annual qty 10000)
63 | 1 | AUX-HV_DAB: 1 | 105k | Resistor 105k 0.1% 0603 |  |  | 0603 | GENERIC |  | 0.003900 | 0.0039 | estimate class:res_0603_0.1pct: GENERIC class rule, reel price of a typical equivalent. LCSC C5126214 FRH0603B1002TS (0603); US$0.0039 at 5000+; 10 kOhm 0.1 %; read 2026... | high | 0.003900 | REAL: class example LCSC C5126214 @5000+ break (annual qty 5000)
64 | 9 | AUX-HV_DAB: 1; DAB60: 8 | 10R | Resistor 10R 1% 0603 |  |  | 0603 | GENERIC |  | 0.003000 | 0.0270 | estimate class:res_0603_1pct: GENERIC class rule, reel price of a typical equivalent. LCSC C2906982 FRC0603F1002TS (0603); US$0.003 at 5000+; 10 kOhm 1 %; read 2026-10... | high | 0.002900 | REAL: class example LCSC C2906982 @10000+ break (annual qty 45000)
65 | 128 | AUX-HV_DAB: 5; BMU-GW: 3; CTRL-C2000: 65; DAB60: 22; SYS-IO-AUX: 33 | 10k | Resistor 10k 1% 0603 |  |  | 0603 | GENERIC |  | 0.003000 | 0.3840 | estimate class:res_0603_1pct: GENERIC class rule, reel price of a typical equivalent. LCSC C2906982 FRC0603F1002TS (0603); US$0.003 at 5000+; 10 kOhm 1 %; read 2026-10... | high | 0.002800 | REAL: class example LCSC C2906982 @50200+ break (annual qty 640000)
66 | 5 | DAB60: 4; SYS-IO-AUX: 1 | 10k | Resistor 10k 1% 0805 |  |  | 0805 | GENERIC |  | 0.001500 | 0.0075 | estimate class:res_0805_1pct: GENERIC class rule, reel price of a typical equivalent. LCSC C17878 0805W8F976JT5E (0805); US$0.0015 at 5000+; 97.6 Ohm 1 %; read 2026-10... | high | 0.001400 | REAL: class example LCSC C17878 @10000+ break (annual qty 25000)
67 | 1 | SYS-IO-AUX: 1 | 10k | Resistor 10k 1% 0603 switch A off when the driver is unpowered |  |  | 0603 | GENERIC |  | 0.003000 | 0.0030 | estimate class:res_0603_1pct: GENERIC class rule, reel price of a typical equivalent. LCSC C2906982 FRC0603F1002TS (0603); US$0.003 at 5000+; 10 kOhm 1 %; read 2026-10... | high | 0.003000 | REAL: class example LCSC C2906982 @5000+ break (annual qty 5000)
68 | 1 | SYS-IO-AUX: 1 | 10k | Resistor 10k 1% 0603 GD switch and switch B off when the driver is unpowered |  |  | 0603 | GENERIC |  | 0.003000 | 0.0030 | estimate class:res_0603_1pct: GENERIC class rule, reel price of a typical equivalent. LCSC C2906982 FRC0603F1002TS (0603); US$0.003 at 5000+; 10 kOhm 1 %; read 2026-10... | high | 0.003000 | REAL: class example LCSC C2906982 @5000+ break (annual qty 5000)
69 | 12 | SYS-IO-AUX: 12 | 10k | Resistor 10k 0.1% 0603 25 ppm |  |  | 0603 | GENERIC |  | 0.003900 | 0.0468 | estimate class:res_0603_0.1pct: GENERIC class rule, reel price of a typical equivalent. LCSC C5126214 FRH0603B1002TS (0603); US$0.0039 at 5000+; 10 kOhm 0.1 %; read 2026... | high | 0.003300 | REAL: class example LCSC C5126214 @50000+ break (annual qty 60000)
70 | 3 | AUX-HV_DAB: 3 | 10k | Resistor 10k 1% 1206 |  |  | 1206 | GENERIC |  | 0.002300 | 0.0069 | estimate class:res_1206_1pct: GENERIC class rule, reel price of a typical equivalent. LCSC C305316 WR12X1581FTL (1206); US$0.0023 at 5000+; 1.58 kOhm 1 %; read 2026-10... | high | 0.002100 | REAL: class example LCSC C305316 @10000+ break (annual qty 15000)
71 | 26 | AUX-HV_DAB: 2; DAB60: 24 | 10k | Resistor 10k 0.1% 0603 |  |  | 0603 | GENERIC |  | 0.003900 | 0.1014 | estimate class:res_0603_0.1pct: GENERIC class rule, reel price of a typical equivalent. LCSC C5126214 FRH0603B1002TS (0603); US$0.0039 at 5000+; 10 kOhm 0.1 %; read 2026... | high | 0.003200 | REAL: class example LCSC C5126214 @100000+ break (annual qty 130000)
72 | 8 | DAB60: 8 | 10k | Resistor 10k 1% 0603 pull-down: open input = gate off |  |  | 0603 | GENERIC |  | 0.003000 | 0.0240 | estimate class:res_0603_1pct: GENERIC class rule, reel price of a typical equivalent. LCSC C2906982 FRC0603F1002TS (0603); US$0.003 at 5000+; 10 kOhm 1 %; read 2026-10... | high | 0.002900 | REAL: class example LCSC C2906982 @10000+ break (annual qty 40000)
73 | 2 | DAB60: 2 | 10k | Resistor 10k 1% 0603 EN pull-down: unpowered logic = drivers disabled |  |  | 0603 | GENERIC |  | 0.003000 | 0.0060 | estimate class:res_0603_1pct: GENERIC class rule, reel price of a typical equivalent. LCSC C2906982 FRC0603F1002TS (0603); US$0.003 at 5000+; 10 kOhm 1 %; read 2026-10... | high | 0.002900 | REAL: class example LCSC C2906982 @10000+ break (annual qty 10000)
74 | 2 | DAB60: 2 | 10k | Resistor 10k 1% 0805 gate-source: off by default, VGS 13 V |  |  | 0805 | GENERIC |  | 0.001500 | 0.0030 | estimate class:res_0805_1pct: GENERIC class rule, reel price of a typical equivalent. LCSC C17878 0805W8F976JT5E (0805); US$0.0015 at 5000+; 97.6 Ohm 1 %; read 2026-10... | high | 0.001400 | REAL: class example LCSC C17878 @10000+ break (annual qty 10000)
75 | 4 | DAB60: 4 | 10k | Resistor 10k 1% 0603 limits the input clamp current on the falling edge |  |  | 0603 | GENERIC |  | 0.003000 | 0.0120 | estimate class:res_0603_1pct: GENERIC class rule, reel price of a typical equivalent. LCSC C2906982 FRC0603F1002TS (0603); US$0.003 at 5000+; 10 kOhm 1 %; read 2026-10... | high | 0.002900 | REAL: class example LCSC C2906982 @10000+ break (annual qty 20000)
76 | 1 | DAB60: 1 | 10k | Resistor 10k 1% 0603 OV monitor unpowered = trip |  |  | 0603 | GENERIC |  | 0.003000 | 0.0030 | estimate class:res_0603_1pct: GENERIC class rule, reel price of a typical equivalent. LCSC C2906982 FRC0603F1002TS (0603); US$0.003 at 5000+; 10 kOhm 1 %; read 2026-10... | high | 0.003000 | REAL: class example LCSC C2906982 @5000+ break (annual qty 5000)
77 | 9 | SYS-IO-AUX: 9 | 10n 100V | Capacitor 10n 10% 100V X7R 0603 |  |  | 0603 | GENERIC |  | 0.011100 | 0.0999 | estimate class:mlcc_0603_x7r_100v_le100n: GENERIC class rule, reel price of a typical equivalent. LCSC C113803 CC0603KRX7R0BB104 (0603); US$0.0111 at 4000+; read 2026-10-04 via th... | high | 0.010700 | REAL: class example LCSC C113803 @8000+ break (annual qty 45000)
78 | 2 | CTRL-C2000: 2 | 10n 16V | Capacitor 10n 16V X7R 0402 |  |  | 0402 | GENERIC |  | 0.004700 | 0.0094 | estimate class:mlcc_0402_x7r_16v_le100n: GENERIC class rule, reel price of a typical equivalent. LCSC C1525 CL05B104KO5NNNC (0402); US$0.0047 at 3000+; read 2026-10-04 via the jl... | high | 0.004400 | REAL: class example LCSC C1525 @10000+ break (annual qty 10000)
79 | 8 | AUX-HV_DAB: 1; CTRL-C2000: 4; SYS-IO-AUX: 3 | 10n 50V | Capacitor 10n 50V X7R 0603 |  |  | 0603 | GENERIC |  | 0.009200 | 0.0736 | estimate class:mlcc_0603_x7r_50v_le100n: GENERIC class rule, reel price of a typical equivalent. LCSC C14663 CC0603KRX7R9BB104 (0603); US$0.0092 at 4000+; read 2026-10-04 via the... | high | 0.009000 | REAL: class example LCSC C14663 @24100+ break (annual qty 40000)
80 | 7 | SYS-IO-AUX: 7 | 10n 50V | Capacitor 10n 10% 50V X7R 0603 |  |  | 0603 | GENERIC |  | 0.009200 | 0.0644 | estimate class:mlcc_0603_x7r_50v_le100n: GENERIC class rule, reel price of a typical equivalent. LCSC C14663 CC0603KRX7R9BB104 (0603); US$0.0092 at 4000+; read 2026-10-04 via the... | high | 0.009000 | REAL: class example LCSC C14663 @24100+ break (annual qty 35000)
81 | 1 | AUX-HV_DAB: 1 | 10n 50V | Capacitor 10n 5% 50V C0G 0805 |  |  | 0805 | GENERIC |  | 0.136200 | 0.1362 | estimate class:mlcc_0805_c0g_50v_le100n: GENERIC class rule, reel price of a typical equivalent. LCSC C97946 GRM31C5C1H104JA01L (1206); US$0.1362 at 4000+; no 0805 C0G >= 10 nF i... | low | 0.136200 | REAL: class example LCSC C97946 @4000+ break (annual qty 5000)
82 | 2 | DAB60: 2 | 10n 50V | Capacitor 10n 50V C0G 0603 |  |  | 0603 | GENERIC |  | 0.028200 | 0.0564 | estimate class:mlcc_0603_c0g_50v_le100n: GENERIC class rule, reel price of a typical equivalent. LCSC C576818 CC0603JRNPO9BN472 (0603); US$0.0282 at 4000+; example is 4.7 nF; rea... | high | 0.026700 | REAL: class example LCSC C576818 @8000+ break (annual qty 10000)
83 | 2 | DAB60: 2 | 10p 50V | Capacitor 10p 5% 50V C0G 0603 |  |  | 0603 | GENERIC |  | 0.005500 | 0.0110 | estimate class:mlcc_0603_c0g_50v_le1n: GENERIC class rule, reel price of a typical equivalent. LCSC C14665 CC0603JRNPO9BN101 (0603); US$0.0055 at 4000+; example is 100 pF; read... | high | 0.005300 | REAL: class example LCSC C14665 @8000+ break (annual qty 10000)
84 | 21 | BMU-GW: 3; CTRL-C2000: 2; DAB60: 4; SYS-IO-AUX: 12 | 10u 16V | Capacitor 10u 16V X7R 0805 |  |  | 0805 | GENERIC |  | 0.054800 | 1.1508 | estimate class:mlcc_0805_x7r_16v_le10u: GENERIC class rule, reel price of a typical equivalent. LCSC C3039694 CL21B106KAYQNNE (0805); US$0.0548 at 4000+; example is 10 uF 25 V;... | high | 0.054800 | REAL: class example LCSC C3039694 @4000+ break (annual qty 105000)
85 | 2 | CTRL-C2000: 2 | 10u 25V | Capacitor 10u 25V X7R 1210 |  |  | 1210 | GENERIC |  | 0.134100 | 0.2682 | estimate class:mlcc_1210_x7r_25v_le10u: GENERIC class rule, reel price of a typical equivalent. LCSC C39232 CL32B106KAJNNNE (1210); US$0.1341 at 5000+; example is 10 uF 25 V; re... | high | 0.134100 | REAL: class example LCSC C39232 @5000+ break (annual qty 10000)
86 | 20 | CTRL-C2000: 5; SYS-IO-AUX: 15 | 10u 50V | Capacitor 10u 10% 50V X7R 1210 |  |  | 1210 | GENERIC |  | 0.148600 | 2.9720 | estimate class:mlcc_1210_x7r_50v_le10u: GENERIC class rule, reel price of a typical equivalent. LCSC C381467 FS32X106K500EGG (1210); US$0.1486 at 5000+; example is 10 uF 50 V; r... | high | 0.148600 | REAL: class example LCSC C381467 @5000+ break (annual qty 100000)
87 | 28 | AUX-HV_DAB: 12; DAB60: 16 | 10u 50V | Capacitor 10u 50V X7R 1210 |  |  | 1210 | GENERIC |  | 0.148600 | 4.1608 | estimate class:mlcc_1210_x7r_50v_le10u: GENERIC class rule, reel price of a typical equivalent. LCSC C381467 FS32X106K500EGG (1210); US$0.1486 at 5000+; example is 10 uF 50 V; r... | high | 0.148600 | REAL: class example LCSC C381467 @5000+ break (annual qty 140000)
88 | 1 | CTRL-C2000: 1 | 10u 6.3V | Capacitor 10u 10% 6.3V X7R 0805 |  |  | 0805 | GENERIC |  | 0.049200 | 0.0492 | estimate class:mlcc_0805_x7r_10v_le10u: GENERIC class rule, reel price of a typical equivalent. LCSC C5189822 CS2012X7R106M100NRE (0805); US$0.0492 at 3000+; example is 10 uF 10... | high | 0.049200 | REAL: class example LCSC C5189822 @3000+ break (annual qty 5000)
89 | 1 | AUX-HV_DAB: 1 | 11.5k | Resistor 11.5k 0.1% 0603 |  |  | 0603 | GENERIC |  | 0.003900 | 0.0039 | estimate class:res_0603_0.1pct: GENERIC class rule, reel price of a typical equivalent. LCSC C5126214 FRH0603B1002TS (0603); US$0.0039 at 5000+; 10 kOhm 0.1 %; read 2026... | high | 0.003900 | REAL: class example LCSC C5126214 @5000+ break (annual qty 5000)
90 | 8 | DAB60: 8 | 113k | Resistor 113k 0.1% 0603 |  |  | 0603 | GENERIC |  | 0.003900 | 0.0312 | estimate class:res_0603_0.1pct: GENERIC class rule, reel price of a typical equivalent. LCSC C5126214 FRH0603B1002TS (0603); US$0.0039 at 5000+; 10 kOhm 0.1 %; read 2026... | high | 0.003500 | REAL: class example LCSC C5126214 @10000+ break (annual qty 40000)
91 | 8 | DAB60: 8 | 118k | Resistor 118k 0.1% 0603 |  |  | 0603 | GENERIC |  | 0.003900 | 0.0312 | estimate class:res_0603_0.1pct: GENERIC class rule, reel price of a typical equivalent. LCSC C5126214 FRH0603B1002TS (0603); US$0.0039 at 5000+; 10 kOhm 0.1 %; read 2026... | high | 0.003500 | REAL: class example LCSC C5126214 @10000+ break (annual qty 40000)
92 | 1 | CTRL-C2000: 1 | 12.1k | Resistor 12.1k 1% 0603 |  |  | 0603 | GENERIC |  | 0.003000 | 0.0030 | estimate class:res_0603_1pct: GENERIC class rule, reel price of a typical equivalent. LCSC C2906982 FRC0603F1002TS (0603); US$0.003 at 5000+; 10 kOhm 1 %; read 2026-10... | high | 0.003000 | REAL: class example LCSC C2906982 @5000+ break (annual qty 5000)
93 | 14 | CTRL-C2000: 4; DAB60: 10 | 120R | Resistor 120R 1% 0603 |  |  | 0603 | GENERIC |  | 0.003000 | 0.0420 | estimate class:res_0603_1pct: GENERIC class rule, reel price of a typical equivalent. LCSC C2906982 FRC0603F1002TS (0603); US$0.003 at 5000+; 10 kOhm 1 %; read 2026-10... | high | 0.002800 | REAL: class example LCSC C2906982 @50200+ break (annual qty 70000)
94 | 3 | BMU-GW: 1; SYS-IO-AUX: 2 | 120R | Resistor 120R 1% 0805 |  |  | 0805 | GENERIC |  | 0.001500 | 0.0045 | estimate class:res_0805_1pct: GENERIC class rule, reel price of a typical equivalent. LCSC C17878 0805W8F976JT5E (0805); US$0.0015 at 5000+; 97.6 Ohm 1 %; read 2026-10... | high | 0.001400 | REAL: class example LCSC C17878 @10000+ break (annual qty 15000)
95 | 1 | CTRL-C2000: 1 | 120k | Resistor 120k 1% 0603 |  |  | 0603 | GENERIC |  | 0.003000 | 0.0030 | estimate class:res_0603_1pct: GENERIC class rule, reel price of a typical equivalent. LCSC C2906982 FRC0603F1002TS (0603); US$0.003 at 5000+; 10 kOhm 1 %; read 2026-10... | high | 0.003000 | REAL: class example LCSC C2906982 @5000+ break (annual qty 5000)
96 | 3 | SYS-IO-AUX: 3 | 121k | Resistor 121k 1% 0603 |  |  | 0603 | GENERIC |  | 0.003000 | 0.0090 | estimate class:res_0603_1pct: GENERIC class rule, reel price of a typical equivalent. LCSC C2906982 FRC0603F1002TS (0603); US$0.003 at 5000+; 10 kOhm 1 %; read 2026-10... | high | 0.002900 | REAL: class example LCSC C2906982 @10000+ break (annual qty 15000)
97 | 8 | DAB60: 8 | 124R | Resistor 124R 1% 0805 |  |  | 0805 | GENERIC |  | 0.001500 | 0.0120 | estimate class:res_0805_1pct: GENERIC class rule, reel price of a typical equivalent. LCSC C17878 0805W8F976JT5E (0805); US$0.0015 at 5000+; 97.6 Ohm 1 %; read 2026-10... | high | 0.001400 | REAL: class example LCSC C17878 @10000+ break (annual qty 40000)
98 | 1 | AUX-HV_DAB: 1 | 13.7k | Resistor 13.7k 1% 0603 |  |  | 0603 | GENERIC |  | 0.003000 | 0.0030 | estimate class:res_0603_1pct: GENERIC class rule, reel price of a typical equivalent. LCSC C2906982 FRC0603F1002TS (0603); US$0.003 at 5000+; 10 kOhm 1 %; read 2026-10... | high | 0.003000 | REAL: class example LCSC C2906982 @5000+ break (annual qty 5000)
99 | 2 | DAB60: 2 | 133k | Resistor 133k 0.1% 0603 hold readback |  |  | 0603 | GENERIC |  | 0.003900 | 0.0078 | estimate class:res_0603_0.1pct: GENERIC class rule, reel price of a typical equivalent. LCSC C5126214 FRH0603B1002TS (0603); US$0.0039 at 5000+; 10 kOhm 0.1 %; read 2026... | high | 0.003500 | REAL: class example LCSC C5126214 @10000+ break (annual qty 10000)
100 | 1 | AUX-HV_DAB: 1 | 137k | Resistor 137k 0.1% 0603 |  |  | 0603 | GENERIC |  | 0.003900 | 0.0039 | estimate class:res_0603_0.1pct: GENERIC class rule, reel price of a typical equivalent. LCSC C5126214 FRH0603B1002TS (0603); US$0.0039 at 5000+; 10 kOhm 0.1 %; read 2026... | high | 0.003900 | REAL: class example LCSC C5126214 @5000+ break (annual qty 5000)
101 | 1 | SYS-IO-AUX: 1 | 14.7k | Resistor 14.7k 1% 0603 |  |  | 0603 | GENERIC |  | 0.003000 | 0.0030 | estimate class:res_0603_1pct: GENERIC class rule, reel price of a typical equivalent. LCSC C2906982 FRC0603F1002TS (0603); US$0.003 at 5000+; 10 kOhm 1 %; read 2026-10... | high | 0.003000 | REAL: class example LCSC C2906982 @5000+ break (annual qty 5000)
102 | 2 | DAB60: 2 | 149k | Resistor 149k 0.1% 0603 |  |  | 0603 | GENERIC |  | 0.003900 | 0.0078 | estimate class:res_0603_0.1pct: GENERIC class rule, reel price of a typical equivalent. LCSC C5126214 FRH0603B1002TS (0603); US$0.0039 at 5000+; 10 kOhm 0.1 %; read 2026... | high | 0.003500 | REAL: class example LCSC C5126214 @10000+ break (annual qty 10000)
103 | 1 | AUX-HV_DAB: 1 | 150R | Resistor 150R 1% 2512 1 W |  |  | 2512 | GENERIC |  | 0.025800 | 0.0258 | estimate class:res_2512_1pct: GENERIC class rule, reel price of a typical equivalent. LCSC C2934076 FRC2512F4702TS (2512); US$0.0258 at 4000+; 47 kOhm 1 W 1 %; read 20... | high | 0.025800 | REAL: class example LCSC C2934076 @4000+ break (annual qty 5000)
104 | 1 | AUX-HV_DAB: 1 | 150n 25V | Capacitor 150n 25V X7R 0603 |  |  | 0603 | GENERIC |  | 0.016000 | 0.0160 | estimate class:mlcc_0603_x7r_25v_le1u: GENERIC class rule, reel price of a typical equivalent. LCSC C29936 CL10B105KA8NNNC (0603); US$0.016 at 4000+; example is 1 uF 25 V; read... | high | 0.016000 | REAL: class example LCSC C29936 @4000+ break (annual qty 5000)
105 | 1 | AUX-HV_DAB: 1 | 150p 50V | Capacitor 150p 50V C0G 0603 |  |  | 0603 | GENERIC |  | 0.005500 | 0.0055 | estimate class:mlcc_0603_c0g_50v_le1n: GENERIC class rule, reel price of a typical equivalent. LCSC C14665 CC0603JRNPO9BN101 (0603); US$0.0055 at 4000+; example is 100 pF; read... | high | 0.005500 | REAL: class example LCSC C14665 @4000+ break (annual qty 5000)
106 | 7 | DAB60: 4; SYS-IO-AUX: 3 | 15k | Resistor 15k 1% 0603 |  |  | 0603 | GENERIC |  | 0.003000 | 0.0210 | estimate class:res_0603_1pct: GENERIC class rule, reel price of a typical equivalent. LCSC C2906982 FRC0603F1002TS (0603); US$0.003 at 5000+; 10 kOhm 1 %; read 2026-10... | high | 0.002900 | REAL: class example LCSC C2906982 @10000+ break (annual qty 35000)
107 | 1 | AUX-HV_DAB: 1 | 15n 50V | Capacitor 15n 5% 50V C0G 0805 |  |  | 0805 | GENERIC |  | 0.136200 | 0.1362 | estimate class:mlcc_0805_c0g_50v_le100n: GENERIC class rule, reel price of a typical equivalent. LCSC C97946 GRM31C5C1H104JA01L (1206); US$0.1362 at 4000+; no 0805 C0G >= 10 nF i... | low | 0.136200 | REAL: class example LCSC C97946 @4000+ break (annual qty 5000)
108 | 1 | SYS-IO-AUX: 1 | 16.9k | Resistor 16.9k 0.1% 0603 10 ppm/K thin film |  |  | 0603 | GENERIC |  | 0.041000 | 0.0410 | estimate class:res_0603_0.1pct_10ppm: GENERIC class rule, reel price of a typical equivalent. LCSC C190610 ERA3AEB103V (0603); US$0.041 at 5000+; Panasonic ERA-3A thin film 0.... | medium | 0.041000 | REAL: class example LCSC C190610 @5000+ break (annual qty 5000)
109 | 1 | AUX-HV_DAB: 1 | 16.9k | Resistor 16.9k 0.1% 0603 |  |  | 0603 | GENERIC |  | 0.003900 | 0.0039 | estimate class:res_0603_0.1pct: GENERIC class rule, reel price of a typical equivalent. LCSC C5126214 FRH0603B1002TS (0603); US$0.0039 at 5000+; 10 kOhm 0.1 %; read 2026... | high | 0.003900 | REAL: class example LCSC C5126214 @5000+ break (annual qty 5000)
110 | 1 | SYS-IO-AUX: 1 | 18.7k | Resistor 18.7k 0.1% 0603 10 ppm/K thin film |  |  | 0603 | GENERIC |  | 0.041000 | 0.0410 | estimate class:res_0603_0.1pct_10ppm: GENERIC class rule, reel price of a typical equivalent. LCSC C190610 ERA3AEB103V (0603); US$0.041 at 5000+; Panasonic ERA-3A thin film 0.... | medium | 0.041000 | REAL: class example LCSC C190610 @5000+ break (annual qty 5000)
111 | 2 | DAB60: 2 | 196k | Resistor 196k 0.1% 0603 |  |  | 0603 | GENERIC |  | 0.003900 | 0.0078 | estimate class:res_0603_0.1pct: GENERIC class rule, reel price of a typical equivalent. LCSC C5126214 FRH0603B1002TS (0603); US$0.0039 at 5000+; 10 kOhm 0.1 %; read 2026... | high | 0.003500 | REAL: class example LCSC C5126214 @10000+ break (annual qty 10000)
112 | 1 | SYS-IO-AUX: 1 | 1M | Resistor 1M 1% 0603 hysteresis |  |  | 0603 | GENERIC |  | 0.003000 | 0.0030 | estimate class:res_0603_1pct: GENERIC class rule, reel price of a typical equivalent. LCSC C2906982 FRC0603F1002TS (0603); US$0.003 at 5000+; 10 kOhm 1 %; read 2026-10... | high | 0.003000 | REAL: class example LCSC C2906982 @5000+ break (annual qty 5000)
113 | 5 | BMU-GW: 1; SYS-IO-AUX: 4 | 1M | Resistor 1M 1% 1206 |  |  | 1206 | GENERIC |  | 0.002300 | 0.0115 | estimate class:res_1206_1pct: GENERIC class rule, reel price of a typical equivalent. LCSC C305316 WR12X1581FTL (1206); US$0.0023 at 5000+; 1.58 kOhm 1 %; read 2026-10... | high | 0.002100 | REAL: class example LCSC C305316 @10000+ break (annual qty 25000)
114 | 11 | AUX-HV_DAB: 3; DAB60: 8 | 1M | Resistor 1M 1% 0603 |  |  | 0603 | GENERIC |  | 0.003000 | 0.0330 | estimate class:res_0603_1pct: GENERIC class rule, reel price of a typical equivalent. LCSC C2906982 FRC0603F1002TS (0603); US$0.003 at 5000+; 10 kOhm 1 %; read 2026-10... | high | 0.002800 | REAL: class example LCSC C2906982 @50200+ break (annual qty 55000)
115 | 8 | DAB60: 8 | 1R | Resistor 1R 1% 2512 Ron, pulse-rated thick film 1 W |  |  | 2512 | GENERIC |  | 0.147800 | 1.1824 | estimate class:res_2512_1pct_pulse: GENERIC class rule, reel price of a typical equivalent. LCSC C2991665 RPL-12K10R0FT (2512); US$0.1478 at 4000+; pulse-rated 2512 thick fi... | low | 0.147800 | REAL: class example LCSC C2991665 @4000+ break (annual qty 40000)
116 | 26 | AUX-HV_DAB: 5; CTRL-C2000: 5; DAB60: 2; SYS-IO-AUX: 14 | 1k | Resistor 1k 1% 0603 |  |  | 0603 | GENERIC |  | 0.003000 | 0.0780 | estimate class:res_0603_1pct: GENERIC class rule, reel price of a typical equivalent. LCSC C2906982 FRC0603F1002TS (0603); US$0.003 at 5000+; 10 kOhm 1 %; read 2026-10... | high | 0.002800 | REAL: class example LCSC C2906982 @50200+ break (annual qty 130000)
117 | 1 | SYS-IO-AUX: 1 | 1k | Resistor 1k 1% 0603 HGATE series R1 |  |  | 0603 | GENERIC |  | 0.003000 | 0.0030 | estimate class:res_0603_1pct: GENERIC class rule, reel price of a typical equivalent. LCSC C2906982 FRC0603F1002TS (0603); US$0.003 at 5000+; 10 kOhm 1 %; read 2026-10... | high | 0.003000 | REAL: class example LCSC C2906982 @5000+ break (annual qty 5000)
118 | 9 | SYS-IO-AUX: 9 | 1k | Resistor 1k 1% MELF 0204 0.25 W RTHR |  |  | MELF 0204 | GENERIC |  | 0.026700 | 0.2403 | estimate class:res_melf0204_1pct: GENERIC class rule, reel price of a typical equivalent. LCSC C1855852 SMM02040C1001FB000 (MELF-0204); US$0.0267 at 5000+; Vishay-type SMM... | high | 0.025300 | REAL: class example LCSC C1855852 @10000+ break (annual qty 45000)
119 | 2 | SYS-IO-AUX: 2 | 1k | Resistor 1k 1% 0603 CTRL input cannot back-drive the chain |  |  | 0603 | GENERIC |  | 0.003000 | 0.0060 | estimate class:res_0603_1pct: GENERIC class rule, reel price of a typical equivalent. LCSC C2906982 FRC0603F1002TS (0603); US$0.003 at 5000+; 10 kOhm 1 %; read 2026-10... | high | 0.002900 | REAL: class example LCSC C2906982 @10000+ break (annual qty 10000)
120 | 4 | SYS-IO-AUX: 4 | 1k | Resistor 1k 1% 0603 SNS unused (datasheet table 6-2) |  |  | 0603 | GENERIC |  | 0.003000 | 0.0120 | estimate class:res_0603_1pct: GENERIC class rule, reel price of a typical equivalent. LCSC C2906982 FRC0603F1002TS (0603); US$0.003 at 5000+; 10 kOhm 1 %; read 2026-10... | high | 0.002900 | REAL: class example LCSC C2906982 @10000+ break (annual qty 20000)
121 | 1 | BMU-GW: 1 | 1k | Resistor 1k 1% 0603 5 mA preload |  |  | 0603 | GENERIC |  | 0.003000 | 0.0030 | estimate class:res_0603_1pct: GENERIC class rule, reel price of a typical equivalent. LCSC C2906982 FRC0603F1002TS (0603); US$0.003 at 5000+; 10 kOhm 1 %; read 2026-10... | high | 0.003000 | REAL: class example LCSC C2906982 @5000+ break (annual qty 5000)
122 | 1 | DAB60: 1 | 1k | Resistor 1k 0.1% 0603 |  |  | 0603 | GENERIC |  | 0.003900 | 0.0039 | estimate class:res_0603_0.1pct: GENERIC class rule, reel price of a typical equivalent. LCSC C5126214 FRH0603B1002TS (0603); US$0.0039 at 5000+; 10 kOhm 0.1 %; read 2026... | high | 0.003900 | REAL: class example LCSC C5126214 @5000+ break (annual qty 5000)
123 | 21 | AUX-HV_DAB: 1; CTRL-C2000: 20 | 1n 50V | Capacitor 1n 5% 50V C0G 0603 |  |  | 0603 | GENERIC |  | 0.005500 | 0.1155 | estimate class:mlcc_0603_c0g_50v_le1n: GENERIC class rule, reel price of a typical equivalent. LCSC C14665 CC0603JRNPO9BN101 (0603); US$0.0055 at 4000+; example is 100 pF; read... | high | 0.005100 | REAL: class example LCSC C14665 @48200+ break (annual qty 105000)
124 | 29 | AUX-HV_DAB: 1; CTRL-C2000: 4; DAB60: 24 | 1n 50V | Capacitor 1n 50V X7R 0603 |  |  | 0603 | GENERIC |  | 0.004300 | 0.1247 | estimate class:mlcc_0603_x7r_50v_le1n: GENERIC class rule, reel price of a typical equivalent. LCSC C1588 CL10B102KB8NNNC (0603); US$0.0043 at 4000+; read 2026-10-04 via the jl... | high | 0.004100 | REAL: class example LCSC C1588 @24100+ break (annual qty 145000)
125 | 7 | DAB60: 2; SYS-IO-AUX: 5 | 1n 50V | Capacitor 1n 10% 50V X7R 0603 |  |  | 0603 | GENERIC |  | 0.004300 | 0.0301 | estimate class:mlcc_0603_x7r_50v_le1n: GENERIC class rule, reel price of a typical equivalent. LCSC C1588 CL10B102KB8NNNC (0603); US$0.0043 at 4000+; read 2026-10-04 via the jl... | high | 0.004100 | REAL: class example LCSC C1588 @24100+ break (annual qty 35000)
126 | 2 | DAB60: 2 | 1n 50V | Capacitor 1n 50V C0G 0603 |  |  | 0603 | GENERIC |  | 0.005500 | 0.0110 | estimate class:mlcc_0603_c0g_50v_le1n: GENERIC class rule, reel price of a typical equivalent. LCSC C14665 CC0603JRNPO9BN101 (0603); US$0.0055 at 4000+; example is 100 pF; read... | high | 0.005300 | REAL: class example LCSC C14665 @8000+ break (annual qty 10000)
127 | 29 | CTRL-C2000: 6; DAB60: 20; SYS-IO-AUX: 3 | 1u 16V | Capacitor 1u 16V X7R 0603 |  |  | 0603 | GENERIC |  | 0.015800 | 0.4582 | estimate class:mlcc_0603_x7r_16v_le1u: GENERIC class rule, reel price of a typical equivalent. LCSC C59782 CL10B105KO8NNNC (0603); US$0.0158 at 4000+; example is 1 uF 16 V; rea... | high | 0.015200 | REAL: class example LCSC C59782 @48000+ break (annual qty 145000)
128 | 3 | CTRL-C2000: 2; SYS-IO-AUX: 1 | 1u 16V | Capacitor 1u 10% 16V X7R 0603 |  |  | 0603 | GENERIC |  | 0.015800 | 0.0474 | estimate class:mlcc_0603_x7r_16v_le1u: GENERIC class rule, reel price of a typical equivalent. LCSC C59782 CL10B105KO8NNNC (0603); US$0.0158 at 4000+; example is 1 uF 16 V; rea... | high | 0.015800 | REAL: class example LCSC C59782 @4000+ break (annual qty 15000)
129 | 1 | AUX-HV_DAB: 1 | 1u 25V | Capacitor 1u 25V X7R 0603 |  |  | 0603 | GENERIC |  | 0.016000 | 0.0160 | estimate class:mlcc_0603_x7r_25v_le1u: GENERIC class rule, reel price of a typical equivalent. LCSC C29936 CL10B105KA8NNNC (0603); US$0.016 at 4000+; example is 1 uF 25 V; read... | high | 0.016000 | REAL: class example LCSC C29936 @4000+ break (annual qty 5000)
130 | 16 | DAB60: 16 | 1u 25V | Capacitor 1u 25V X7R 0805 |  |  | 0805 | GENERIC |  | 0.035800 | 0.5728 | estimate class:mlcc_0805_x7r_25v_le1u: GENERIC class rule, reel price of a typical equivalent. LCSC C28323 CL21B105KBFNNNE (0805); US$0.0358 at 2000+; example is 1 uF 50 V; rea... | high | 0.034500 | REAL: class example LCSC C28323 @20000+ break (annual qty 80000)
131 | 6 | CTRL-C2000: 6 | 1u 50V | Capacitor 1u 50V X7R 1206 |  |  | 1206 | GENERIC |  | 0.035800 | 0.2148 | estimate class:mlcc_1206_x7r_50v_le1u: GENERIC class rule, reel price of a typical equivalent. LCSC C1848 CL31B105KBHNNNE (1206); US$0.0358 at 4000+; example is 1 uF 50 V; read... | high | 0.035200 | REAL: class example LCSC C1848 @10000+ break (annual qty 30000)
132 | 2 | DAB60: 2 | 1u 50V | Capacitor 1u 10% 50V X7R 1206 |  |  | 1206 | GENERIC |  | 0.035800 | 0.0716 | estimate class:mlcc_1206_x7r_50v_le1u: GENERIC class rule, reel price of a typical equivalent. LCSC C1848 CL31B105KBHNNNE (1206); US$0.0358 at 4000+; example is 1 uF 50 V; read... | high | 0.035200 | REAL: class example LCSC C1848 @10000+ break (annual qty 10000)
133 | 14 | CTRL-C2000: 14 | 1u 6.3V | Capacitor 1u 10% 6.3V X7R 0402 |  |  | 0402 | GENERIC |  | 0.003800 | 0.0532 | estimate class:mlcc_0402_x7r_10v_le1u: GENERIC class rule, reel price of a typical equivalent. LCSC C5448871 TCC0402X7R105K6R3AT (0402); US$0.0038 at 1500+; read 2026-10-04 via... | high | 0.002800 | REAL: class example LCSC C5448871 @50000+ break (annual qty 70000)
134 | 1 | SYS-IO-AUX: 1 | 2.00k | Resistor 2.00k 0.1% 0603 10 ppm/K thin film |  |  | 0603 | GENERIC |  | 0.041000 | 0.0410 | estimate class:res_0603_0.1pct_10ppm: GENERIC class rule, reel price of a typical equivalent. LCSC C190610 ERA3AEB103V (0603); US$0.041 at 5000+; Panasonic ERA-3A thin film 0.... | medium | 0.041000 | REAL: class example LCSC C190610 @5000+ break (annual qty 5000)
135 | 1 | SYS-IO-AUX: 1 | 2.15k | Resistor 2.15k 0.1% 0603 10 ppm/K thin film |  |  | 0603 | GENERIC |  | 0.041000 | 0.0410 | estimate class:res_0603_0.1pct_10ppm: GENERIC class rule, reel price of a typical equivalent. LCSC C190610 ERA3AEB103V (0603); US$0.041 at 5000+; Panasonic ERA-3A thin film 0.... | medium | 0.041000 | REAL: class example LCSC C190610 @5000+ break (annual qty 5000)
136 | 4 | DAB60: 4 | 2.1k | Resistor 2.1k 0.1% 0603 |  |  | 0603 | GENERIC |  | 0.003900 | 0.0156 | estimate class:res_0603_0.1pct: GENERIC class rule, reel price of a typical equivalent. LCSC C5126214 FRH0603B1002TS (0603); US$0.0039 at 5000+; 10 kOhm 0.1 %; read 2026... | high | 0.003500 | REAL: class example LCSC C5126214 @10000+ break (annual qty 20000)
137 | 8 | DAB60: 8 | 2.21k | Resistor 2.21k 1% 0603 |  |  | 0603 | GENERIC |  | 0.003000 | 0.0240 | estimate class:res_0603_1pct: GENERIC class rule, reel price of a typical equivalent. LCSC C2906982 FRC0603F1002TS (0603); US$0.003 at 5000+; 10 kOhm 1 %; read 2026-10... | high | 0.002900 | REAL: class example LCSC C2906982 @10000+ break (annual qty 40000)
138 | 6 | AUX-HV_DAB: 1; CTRL-C2000: 5 | 2.2k | Resistor 2.2k 1% 0603 |  |  | 0603 | GENERIC |  | 0.003000 | 0.0180 | estimate class:res_0603_1pct: GENERIC class rule, reel price of a typical equivalent. LCSC C2906982 FRC0603F1002TS (0603); US$0.003 at 5000+; 10 kOhm 1 %; read 2026-10... | high | 0.002900 | REAL: class example LCSC C2906982 @10000+ break (annual qty 30000)
139 | 1 | SYS-IO-AUX: 1 | 2.2k | Resistor 2.2k 1% 1206 |  |  | 1206 | GENERIC |  | 0.002300 | 0.0023 | estimate class:res_1206_1pct: GENERIC class rule, reel price of a typical equivalent. LCSC C305316 WR12X1581FTL (1206); US$0.0023 at 5000+; 1.58 kOhm 1 %; read 2026-10... | high | 0.002300 | REAL: class example LCSC C305316 @5000+ break (annual qty 5000)
140 | 1 | SYS-IO-AUX: 1 | 2.2k | Resistor 2.2k 1% 2010 0.75 W |  |  | 2010 | GENERIC |  | 0.010600 | 0.0106 | estimate class:res_2010_1pct: GENERIC class rule, reel price of a typical equivalent. LCSC C7467392 FRC2010F2201TS (2010); US$0.0106 at 4000+; 2.2 kOhm 1 %; read 2026-... | high | 0.010600 | REAL: class example LCSC C7467392 @4000+ break (annual qty 5000)
141 | 1 | AUX-HV_DAB: 1 | 2.2n 50V | Capacitor 2.2n 50V C0G 0603 |  |  | 0603 | GENERIC |  | 0.028200 | 0.0282 | estimate class:mlcc_0603_c0g_50v_le100n: GENERIC class rule, reel price of a typical equivalent. LCSC C576818 CC0603JRNPO9BN472 (0603); US$0.0282 at 4000+; example is 4.7 nF; rea... | high | 0.028200 | REAL: class example LCSC C576818 @4000+ break (annual qty 5000)
142 | 1 | SYS-IO-AUX: 1 | 2.2u 100V | Capacitor 2.2u 10% 100V X7R 1210 |  |  | 1210 | GENERIC |  | 0.060400 | 0.0604 | estimate class:mlcc_1210_x7r_100v_le10u: GENERIC class rule, reel price of a typical equivalent. LCSC C153036 FS32X225K101EGG (1210); US$0.0604 at 5000+; example is 2.2 uF 100 V;... | high | 0.060400 | REAL: class example LCSC C153036 @5000+ break (annual qty 5000)
143 | 4 | AUX-HV_DAB: 1; CTRL-C2000: 1; DAB60: 2 | 2.2u 16V | Capacitor 2.2u 16V X7R 0603 |  |  | 0603 | GENERIC |  | 0.016300 | 0.0652 | estimate class:mlcc_0603_x7r_16v_le10u: GENERIC class rule, reel price of a typical equivalent. LCSC C43922 0603B225K160NT (0603); US$0.0163 at 4000+; example is 2.2 uF 16 V; re... | high | 0.016300 | REAL: class example LCSC C43922 @4000+ break (annual qty 20000)
144 | 6 | CTRL-C2000: 2; SYS-IO-AUX: 4 | 2.2u 16V | Capacitor 2.2u 10% 16V X7R 0603 |  |  | 0603 | GENERIC |  | 0.016300 | 0.0978 | estimate class:mlcc_0603_x7r_16v_le10u: GENERIC class rule, reel price of a typical equivalent. LCSC C43922 0603B225K160NT (0603); US$0.0163 at 4000+; example is 2.2 uF 16 V; re... | high | 0.015200 | REAL: class example LCSC C43922 @24000+ break (annual qty 30000)
145 | 1 | AUX-HV_DAB: 1 | 2.2u 25V | Capacitor 2.2u 10% 25V X7R 1206 |  |  | 1206 | GENERIC |  | 0.047100 | 0.0471 | estimate class:mlcc_1206_x7r_25v_le10u: GENERIC class rule, reel price of a typical equivalent. LCSC C51205 CL31B475KBHNNNE (1206); US$0.0471 at 4000+; example is 4.7 uF rated 5... | high | 0.047100 | REAL: class example LCSC C51205 @4000+ break (annual qty 5000)
146 | 8 | DAB60: 8 | 2.2u 50V | Capacitor 2.2u 50V X7R 0805 |  |  | 0805 | GENERIC |  | 0.058900 | 0.4712 | estimate class:mlcc_0805_x7r_50v_le10u: GENERIC class rule, reel price of a typical equivalent. LCSC C125847 CC0805KKX7R9BB225 (0805); US$0.0589 at 3000+; example is 2.2 uF 50 V... | high | 0.057300 | REAL: class example LCSC C125847 @21000+ break (annual qty 40000)
147 | 2 | CTRL-C2000: 2 | 2.49k | Resistor 2.49k 1% 0603 |  |  | 0603 | GENERIC |  | 0.003000 | 0.0060 | estimate class:res_0603_1pct: GENERIC class rule, reel price of a typical equivalent. LCSC C2906982 FRC0603F1002TS (0603); US$0.003 at 5000+; 10 kOhm 1 %; read 2026-10... | high | 0.002900 | REAL: class example LCSC C2906982 @10000+ break (annual qty 10000)
148 | 1 | DAB60: 1 | 2.61k | Resistor 2.61k 0.1% 0603 board ID DAB60-PORT with the readback network |  |  | 0603 | GENERIC |  | 0.003900 | 0.0039 | estimate class:res_0603_0.1pct: GENERIC class rule, reel price of a typical equivalent. LCSC C5126214 FRH0603B1002TS (0603); US$0.0039 at 5000+; 10 kOhm 0.1 %; read 2026... | high | 0.003900 | REAL: class example LCSC C5126214 @5000+ break (annual qty 5000)
149 | 2 | DAB60: 2 | 2.94k | Resistor 2.94k 1% 1206 |  |  | 1206 | GENERIC |  | 0.002300 | 0.0046 | estimate class:res_1206_1pct: GENERIC class rule, reel price of a typical equivalent. LCSC C305316 WR12X1581FTL (1206); US$0.0023 at 5000+; 1.58 kOhm 1 %; read 2026-10... | high | 0.002100 | REAL: class example LCSC C305316 @10000+ break (annual qty 10000)
150 | 1 | DAB60: 1 | 20.0k | Resistor 20.0k 0.1% 0603 board ID DAB60-B1 (interfaces.ID_OHM) |  |  | 0603 | GENERIC |  | 0.003900 | 0.0039 | estimate class:res_0603_0.1pct: GENERIC class rule, reel price of a typical equivalent. LCSC C5126214 FRH0603B1002TS (0603); US$0.0039 at 5000+; 10 kOhm 0.1 %; read 2026... | high | 0.003900 | REAL: class example LCSC C5126214 @5000+ break (annual qty 5000)
151 | 4 | DAB60: 4 | 20.0k | Resistor 20.0k 0.1% 0603 |  |  | 0603 | GENERIC |  | 0.003900 | 0.0156 | estimate class:res_0603_0.1pct: GENERIC class rule, reel price of a typical equivalent. LCSC C5126214 FRH0603B1002TS (0603); US$0.0039 at 5000+; 10 kOhm 0.1 %; read 2026... | high | 0.003500 | REAL: class example LCSC C5126214 @10000+ break (annual qty 20000)
152 | 2 | SYS-IO-AUX: 2 | 200k | Resistor 200k 1% 0603 |  |  | 0603 | GENERIC |  | 0.003000 | 0.0060 | estimate class:res_0603_1pct: GENERIC class rule, reel price of a typical equivalent. LCSC C2906982 FRC0603F1002TS (0603); US$0.003 at 5000+; 10 kOhm 1 %; read 2026-10... | high | 0.002900 | REAL: class example LCSC C2906982 @10000+ break (annual qty 10000)
153 | 8 | DAB60: 8 | 220R | Resistor 220R 1% 0603 |  |  | 0603 | GENERIC |  | 0.003000 | 0.0240 | estimate class:res_0603_1pct: GENERIC class rule, reel price of a typical equivalent. LCSC C2906982 FRC0603F1002TS (0603); US$0.003 at 5000+; 10 kOhm 1 %; read 2026-10... | high | 0.002900 | REAL: class example LCSC C2906982 @10000+ break (annual qty 40000)
154 | 2 | DAB60: 2 | 220k | Resistor 220k 1% 0603 SPD_N high = varistor network open |  |  | 0603 | GENERIC |  | 0.003000 | 0.0060 | estimate class:res_0603_1pct: GENERIC class rule, reel price of a typical equivalent. LCSC C2906982 FRC0603F1002TS (0603); US$0.003 at 5000+; 10 kOhm 1 %; read 2026-10... | high | 0.002900 | REAL: class example LCSC C2906982 @10000+ break (annual qty 10000)
155 | 3 | DAB60: 3 | 220n 50V | Capacitor 220n 50V X7R 0603 |  |  | 0603 | GENERIC |  | 0.009100 | 0.0273 | estimate class:mlcc_0603_x7r_50v_le1u: GENERIC class rule, reel price of a typical equivalent. LCSC C64705 CL10B224KB8NNNC (0603); US$0.0091 at 4000+; example is 220 nF; read 2... | high | 0.008600 | REAL: class example LCSC C64705 @8000+ break (annual qty 15000)
156 | 1 | AUX-HV_DAB: 1 | 220p 50V | Capacitor 220p 50V C0G 0603 |  |  | 0603 | GENERIC |  | 0.005500 | 0.0055 | estimate class:mlcc_0603_c0g_50v_le1n: GENERIC class rule, reel price of a typical equivalent. LCSC C14665 CC0603JRNPO9BN101 (0603); US$0.0055 at 4000+; example is 100 pF; read... | high | 0.005500 | REAL: class example LCSC C14665 @4000+ break (annual qty 5000)
157 | 1 | AUX-HV_DAB: 1 | 22R | Resistor 22R 1% 0603 |  |  | 0603 | GENERIC |  | 0.003000 | 0.0030 | estimate class:res_0603_1pct: GENERIC class rule, reel price of a typical equivalent. LCSC C2906982 FRC0603F1002TS (0603); US$0.003 at 5000+; 10 kOhm 1 %; read 2026-10... | high | 0.003000 | REAL: class example LCSC C2906982 @5000+ break (annual qty 5000)
158 | 2 | AUX-HV_DAB: 2 | 22k | Resistor 22k 1% 0603 |  |  | 0603 | GENERIC |  | 0.003000 | 0.0060 | estimate class:res_0603_1pct: GENERIC class rule, reel price of a typical equivalent. LCSC C2906982 FRC0603F1002TS (0603); US$0.003 at 5000+; 10 kOhm 1 %; read 2026-10... | high | 0.002900 | REAL: class example LCSC C2906982 @10000+ break (annual qty 10000)
159 | 4 | DAB60: 4 | 22k | Resistor 22k 1% 0603 gate-GND: off when the gate source is off |  |  | 0603 | GENERIC |  | 0.003000 | 0.0120 | estimate class:res_0603_1pct: GENERIC class rule, reel price of a typical equivalent. LCSC C2906982 FRC0603F1002TS (0603); US$0.003 at 5000+; 10 kOhm 1 %; read 2026-10... | high | 0.002900 | REAL: class example LCSC C2906982 @10000+ break (annual qty 20000)
160 | 2 | DAB60: 2 | 22k | Resistor 22k 1% 0603 gate-GND |  |  | 0603 | GENERIC |  | 0.003000 | 0.0060 | estimate class:res_0603_1pct: GENERIC class rule, reel price of a typical equivalent. LCSC C2906982 FRC0603F1002TS (0603); US$0.003 at 5000+; 10 kOhm 1 %; read 2026-10... | high | 0.002900 | REAL: class example LCSC C2906982 @10000+ break (annual qty 10000)
161 | 8 | SYS-IO-AUX: 8 | 22n 16V | Capacitor 22n 10% 16V X7R 0603 |  |  | 0603 | GENERIC |  | 0.009200 | 0.0736 | estimate class:mlcc_0603_x7r_16v_le100n: GENERIC class rule, reel price of a typical equivalent. LCSC C14663 CC0603KRX7R9BB104 (0603); US$0.0092 at 4000+; example is rated 50 V (... | high | 0.009000 | REAL: class example LCSC C14663 @24100+ break (annual qty 40000)
162 | 2 | AUX-HV_DAB: 2 | 22n 2kV | Capacitor 22n 2kV X7R 1812 |  |  | 1812 | GENERIC |  | 0.193300 | 0.3866 | estimate class:mlcc_1812_x7r_2kv_le100n: GENERIC class rule, reel price of a typical equivalent. LCSC C5290328 FV43X223K202EGG (1812); US$0.1933 at 5000+; example is 22 nF 2 kV X... | high | 0.193300 | REAL: class example LCSC C5290328 @5000+ break (annual qty 10000)
163 | 4 | CTRL-C2000: 4 | 22u 10V | Capacitor 22u 10% 10V X7R 0805 |  |  | 0805 | GENERIC |  | 0.462900 | 1.8516 | estimate class:mlcc_0805_x7r_10v_gt10u: GENERIC class rule, reel price of a typical equivalent. LCSC C907991 GRM21BZ71A226ME15L (0805); US$0.4629 at 3000+; example is 22 uF 10 V... | high | 0.459600 | REAL: class example LCSC C907991 @6000+ break (annual qty 20000)
164 | 4 | CTRL-C2000: 4 | 22u 10V | Capacitor 22u 10% 10V X7R 1206 |  |  | 1206 | GENERIC |  | 0.068200 | 0.2728 | estimate class:mlcc_1206_x7r_10v_gt10u: GENERIC class rule, reel price of a typical equivalent. LCSC C87996 CL31B226KPHNNNE (1206); US$0.0682 at 4000+; example is 22 uF 10 V; re... | high | 0.068200 | REAL: class example LCSC C87996 @4000+ break (annual qty 20000)
165 | 6 | DAB60: 6 | 22u 10V | Capacitor 22u 10V X7R 1206 |  |  | 1206 | GENERIC |  | 0.068200 | 0.4092 | estimate class:mlcc_1206_x7r_10v_gt10u: GENERIC class rule, reel price of a typical equivalent. LCSC C87996 CL31B226KPHNNNE (1206); US$0.0682 at 4000+; example is 22 uF 10 V; re... | high | 0.068200 | REAL: class example LCSC C87996 @4000+ break (annual qty 30000)
166 | 3 | CTRL-C2000: 3 | 22u 16V | Capacitor 22u 10% 16V X7R 1206 |  |  | 1206 | GENERIC |  | 0.084600 | 0.2538 | estimate class:mlcc_1206_x7r_16v_gt10u: GENERIC class rule, reel price of a typical equivalent. LCSC C5252682 CS3216X7R226K160NRI (1206); US$0.0846 at 4000+; example is 22 uF 16... | high | 0.084600 | REAL: class example LCSC C5252682 @4000+ break (annual qty 15000)
167 | 2 | SYS-IO-AUX: 2 | 22u 16V | Capacitor 22u 20% 16V X7R 1210 |  |  | 1210 | GENERIC |  | 0.130200 | 0.2604 | estimate class:mlcc_1210_x7r_16v_gt10u: GENERIC class rule, reel price of a typical equivalent. LCSC C2918511 CS3225X7R226K250NRL (1210); US$0.1302 at 5000+; example is 22 uF 25... | medium | 0.130200 | REAL: class example LCSC C2918511 @5000+ break (annual qty 10000)
168 | 16 | DAB60: 16 | 22u 25V | Capacitor 22u 25V X7R 1210 |  |  | 1210 | GENERIC |  | 0.130200 | 2.0832 | estimate class:mlcc_1210_x7r_25v_gt10u: GENERIC class rule, reel price of a typical equivalent. LCSC C2918511 CS3225X7R226K250NRL (1210); US$0.1302 at 5000+; example is 22 uF 25... | high | 0.130200 | REAL: class example LCSC C2918511 @5000+ break (annual qty 80000)
169 | 2 | DAB60: 2 | 22u 25V | Capacitor 22u 10% 25V X7R 1206 |  |  | 1206 | GENERIC |  | 0.084600 | 0.1692 | estimate class:mlcc_1206_x7r_25v_gt10u: GENERIC class rule, reel price of a typical equivalent. LCSC C5252682 CS3216X7R226K160NRI (1206); US$0.0846 at 4000+; no 22 uF 25 V X7R i... | medium | 0.084600 | REAL: class example LCSC C5252682 @4000+ break (annual qty 10000)
170 | 12 | CTRL-C2000: 1; DAB60: 10; SYS-IO-AUX: 1 | 24.9k | Resistor 24.9k 1% 0603 |  |  | 0603 | GENERIC |  | 0.003000 | 0.0360 | estimate class:res_0603_1pct: GENERIC class rule, reel price of a typical equivalent. LCSC C2906982 FRC0603F1002TS (0603); US$0.003 at 5000+; 10 kOhm 1 %; read 2026-10... | high | 0.002800 | REAL: class example LCSC C2906982 @50200+ break (annual qty 60000)
171 | 4 | DAB60: 4 | 25.5k | Resistor 25.5k 1% 0603 |  |  | 0603 | GENERIC |  | 0.003000 | 0.0120 | estimate class:res_0603_1pct: GENERIC class rule, reel price of a typical equivalent. LCSC C2906982 FRC0603F1002TS (0603); US$0.003 at 5000+; 10 kOhm 1 %; read 2026-10... | high | 0.002900 | REAL: class example LCSC C2906982 @10000+ break (annual qty 20000)
172 | 2 | DAB60: 2 | 270n 25V | Capacitor 270n 5% 25V C0G 1210 |  |  | 1210 | GENERIC |  | 0.136200 | 0.2724 | estimate class:mlcc_1210_c0g_25v_le1u: GENERIC class rule, reel price of a typical equivalent. LCSC C97946 GRM31C5C1H104JA01L (1206); US$0.1362 at 4000+; no 270 nF C0G 1210 on... | low | 0.136200 | REAL: class example LCSC C97946 @4000+ break (annual qty 10000)
173 | 2 | SYS-IO-AUX: 2 | 28.7k | Resistor 28.7k 1% 0603 |  |  | 0603 | GENERIC |  | 0.003000 | 0.0060 | estimate class:res_0603_1pct: GENERIC class rule, reel price of a typical equivalent. LCSC C2906982 FRC0603F1002TS (0603); US$0.003 at 5000+; 10 kOhm 1 %; read 2026-10... | high | 0.002900 | REAL: class example LCSC C2906982 @10000+ break (annual qty 10000)
174 | 2 | DAB60: 2 | 2k | Resistor 2k 0.1% 0603 |  |  | 0603 | GENERIC |  | 0.003900 | 0.0078 | estimate class:res_0603_0.1pct: GENERIC class rule, reel price of a typical equivalent. LCSC C5126214 FRH0603B1002TS (0603); US$0.0039 at 5000+; 10 kOhm 0.1 %; read 2026... | high | 0.003500 | REAL: class example LCSC C5126214 @10000+ break (annual qty 10000)
175 | 2 | SYS-IO-AUX: 2 | 3.01k | Resistor 3.01k 1% 0603 |  |  | 0603 | GENERIC |  | 0.003000 | 0.0060 | estimate class:res_0603_1pct: GENERIC class rule, reel price of a typical equivalent. LCSC C2906982 FRC0603F1002TS (0603); US$0.003 at 5000+; 10 kOhm 1 %; read 2026-10... | high | 0.002900 | REAL: class example LCSC C2906982 @10000+ break (annual qty 10000)
176 | 2 | CTRL-C2000: 2 | 3.3n 50V | Capacitor 3.3n 10% 50V X7R 0603 |  |  | 0603 | GENERIC |  | 0.009200 | 0.0184 | estimate class:mlcc_0603_x7r_50v_le100n: GENERIC class rule, reel price of a typical equivalent. LCSC C14663 CC0603KRX7R9BB104 (0603); US$0.0092 at 4000+; read 2026-10-04 via the... | high | 0.009200 | REAL: class example LCSC C14663 @4000+ break (annual qty 10000)
177 | 4 | DAB60: 4 | 3.3u 25V | Capacitor 3.3u 10% 25V X7R 0805 |  |  | 0805 | GENERIC |  | 0.018400 | 0.0736 | estimate class:mlcc_0805_x7r_25v_le10u: GENERIC class rule, reel price of a typical equivalent. LCSC C7393948 TCC0805X7R335K250FT (0805); US$0.0184 at 3000+; example is 3.3 uF 2... | medium | 0.016400 | REAL: class example LCSC C7393948 @9000+ break (annual qty 20000)
178 | 1 | AUX-HV_DAB: 1 | 3.57M | Resistor 3.57M 1% 0603 |  |  | 0603 | GENERIC |  | 0.003000 | 0.0030 | estimate class:res_0603_1pct: GENERIC class rule, reel price of a typical equivalent. LCSC C2906982 FRC0603F1002TS (0603); US$0.003 at 5000+; 10 kOhm 1 %; read 2026-10... | high | 0.003000 | REAL: class example LCSC C2906982 @5000+ break (annual qty 5000)
179 | 1 | SYS-IO-AUX: 1 | 3.57k | Resistor 3.57k 1% 0603 |  |  | 0603 | GENERIC |  | 0.003000 | 0.0030 | estimate class:res_0603_1pct: GENERIC class rule, reel price of a typical equivalent. LCSC C2906982 FRC0603F1002TS (0603); US$0.003 at 5000+; 10 kOhm 1 %; read 2026-10... | high | 0.003000 | REAL: class example LCSC C2906982 @5000+ break (annual qty 5000)
180 | 1 | DAB60: 1 | 3.65k | Resistor 3.65k 0.1% 0603 |  |  | 0603 | GENERIC |  | 0.003900 | 0.0039 | estimate class:res_0603_0.1pct: GENERIC class rule, reel price of a typical equivalent. LCSC C5126214 FRH0603B1002TS (0603); US$0.0039 at 5000+; 10 kOhm 0.1 %; read 2026... | high | 0.003900 | REAL: class example LCSC C5126214 @5000+ break (annual qty 5000)
181 | 8 | DAB60: 8 | 3.74k | Resistor 3.74k 1% 1206 |  |  | 1206 | GENERIC |  | 0.002300 | 0.0184 | estimate class:res_1206_1pct: GENERIC class rule, reel price of a typical equivalent. LCSC C305316 WR12X1581FTL (1206); US$0.0023 at 5000+; 1.58 kOhm 1 %; read 2026-10... | high | 0.002100 | REAL: class example LCSC C305316 @10000+ break (annual qty 40000)
182 | 2 | SYS-IO-AUX: 2 | 330R | Resistor 330R 1% 0603 |  |  | 0603 | GENERIC |  | 0.003000 | 0.0060 | estimate class:res_0603_1pct: GENERIC class rule, reel price of a typical equivalent. LCSC C2906982 FRC0603F1002TS (0603); US$0.003 at 5000+; 10 kOhm 1 %; read 2026-10... | high | 0.002900 | REAL: class example LCSC C2906982 @10000+ break (annual qty 10000)
183 | 16 | DAB60: 16 | 330p 50V | Capacitor 330p 5% 50V C0G 0603 |  |  | 0603 | GENERIC |  | 0.005500 | 0.0880 | estimate class:mlcc_0603_c0g_50v_le1n: GENERIC class rule, reel price of a typical equivalent. LCSC C14665 CC0603JRNPO9BN101 (0603); US$0.0055 at 4000+; example is 100 pF; read... | high | 0.005100 | REAL: class example LCSC C14665 @48200+ break (annual qty 80000)
184 | 3 | CTRL-C2000: 3 | 33R | Resistor 33R 1% 0603 |  |  | 0603 | GENERIC |  | 0.003000 | 0.0090 | estimate class:res_0603_1pct: GENERIC class rule, reel price of a typical equivalent. LCSC C2906982 FRC0603F1002TS (0603); US$0.003 at 5000+; 10 kOhm 1 %; read 2026-10... | high | 0.002900 | REAL: class example LCSC C2906982 @10000+ break (annual qty 15000)
185 | 1 | AUX-HV_DAB: 1 | 33k | Resistor 33k 1% 0603 |  |  | 0603 | GENERIC |  | 0.003000 | 0.0030 | estimate class:res_0603_1pct: GENERIC class rule, reel price of a typical equivalent. LCSC C2906982 FRC0603F1002TS (0603); US$0.003 at 5000+; 10 kOhm 1 %; read 2026-10... | high | 0.003000 | REAL: class example LCSC C2906982 @5000+ break (annual qty 5000)
186 | 1 | AUX-HV_DAB: 1 | 39n 50V | Capacitor 39n 50V X7R 0603 |  |  | 0603 | GENERIC |  | 0.009200 | 0.0092 | estimate class:mlcc_0603_x7r_50v_le100n: GENERIC class rule, reel price of a typical equivalent. LCSC C14663 CC0603KRX7R9BB104 (0603); US$0.0092 at 4000+; read 2026-10-04 via the... | high | 0.009200 | REAL: class example LCSC C14663 @4000+ break (annual qty 5000)
187 | 24 | CTRL-C2000: 24 | 4.02k | Resistor 4.02k 0.1% 0603 10ppm/K |  |  | 0603 | GENERIC |  | 0.041000 | 0.9840 | estimate class:res_0603_0.1pct_10ppm: GENERIC class rule, reel price of a typical equivalent. LCSC C190610 ERA3AEB103V (0603); US$0.041 at 5000+; Panasonic ERA-3A thin film 0.... | medium | 0.038900 | REAL: class example LCSC C190610 @10000+ break (annual qty 120000)
188 | 2 | DAB60: 2 | 4.7M | Resistor 4.7M 1% 0603 |  |  | 0603 | GENERIC |  | 0.003000 | 0.0060 | estimate class:res_0603_1pct: GENERIC class rule, reel price of a typical equivalent. LCSC C2906982 FRC0603F1002TS (0603); US$0.003 at 5000+; 10 kOhm 1 %; read 2026-10... | high | 0.002900 | REAL: class example LCSC C2906982 @10000+ break (annual qty 10000)
189 | 14 | AUX-HV_DAB: 4; CTRL-C2000: 2; SYS-IO-AUX: 8 | 4.7k | Resistor 4.7k 1% 0603 |  |  | 0603 | GENERIC |  | 0.003000 | 0.0420 | estimate class:res_0603_1pct: GENERIC class rule, reel price of a typical equivalent. LCSC C2906982 FRC0603F1002TS (0603); US$0.003 at 5000+; 10 kOhm 1 %; read 2026-10... | high | 0.002800 | REAL: class example LCSC C2906982 @50200+ break (annual qty 70000)
190 | 1 | SYS-IO-AUX: 1 | 4.7k | Resistor 4.7k 1% 0603 fan supplies off when the gate is unpowered |  |  | 0603 | GENERIC |  | 0.003000 | 0.0030 | estimate class:res_0603_1pct: GENERIC class rule, reel price of a typical equivalent. LCSC C2906982 FRC0603F1002TS (0603); US$0.003 at 5000+; 10 kOhm 1 %; read 2026-10... | high | 0.003000 | REAL: class example LCSC C2906982 @5000+ break (annual qty 5000)
191 | 2 | SYS-IO-AUX: 2 | 4.7n 100V | Capacitor 4.7n 10% 100V X7R 0603 |  |  | 0603 | GENERIC |  | 0.011100 | 0.0222 | estimate class:mlcc_0603_x7r_100v_le100n: GENERIC class rule, reel price of a typical equivalent. LCSC C113803 CC0603KRX7R0BB104 (0603); US$0.0111 at 4000+; read 2026-10-04 via th... | high | 0.010700 | REAL: class example LCSC C113803 @8000+ break (annual qty 10000)
192 | 1 | BMU-GW: 1 | 4.7n 100V | Capacitor 4.7n 100V X7R 0603 |  |  | 0603 | GENERIC |  | 0.011100 | 0.0111 | estimate class:mlcc_0603_x7r_100v_le100n: GENERIC class rule, reel price of a typical equivalent. LCSC C113803 CC0603KRX7R0BB104 (0603); US$0.0111 at 4000+; read 2026-10-04 via th... | high | 0.011100 | REAL: class example LCSC C113803 @4000+ break (annual qty 5000)
193 | 4 | SYS-IO-AUX: 4 | 4.7n 1kV | Capacitor 4.7n 10% 1kV X7R 1206 |  |  | 1206 | GENERIC |  | 0.025400 | 0.1016 | estimate class:mlcc_1206_x7r_1kv_le100n: GENERIC class rule, reel price of a typical equivalent. LCSC C107198 CC1206KKX7RCBB472 (1206); US$0.0254 at 3000+; example is 4.7 nF 1 kV... | high | 0.024100 | REAL: class example LCSC C107198 @6000+ break (annual qty 20000)
194 | 1 | BMU-GW: 1 | 4.7n 1kV | Capacitor 4.7n 1kV X7R 1206 |  |  | 1206 | GENERIC |  | 0.025400 | 0.0254 | estimate class:mlcc_1206_x7r_1kv_le100n: GENERIC class rule, reel price of a typical equivalent. LCSC C107198 CC1206KKX7RCBB472 (1206); US$0.0254 at 3000+; example is 4.7 nF 1 kV... | high | 0.025400 | REAL: class example LCSC C107198 @3000+ break (annual qty 5000)
195 | 6 | DAB60: 6 | 4.7n 50V | Capacitor 4.7n 5% 50V C0G 0603 |  |  | 0603 | GENERIC |  | 0.028200 | 0.1692 | estimate class:mlcc_0603_c0g_50v_le100n: GENERIC class rule, reel price of a typical equivalent. LCSC C576818 CC0603JRNPO9BN472 (0603); US$0.0282 at 4000+; example is 4.7 nF; rea... | high | 0.025900 | REAL: class example LCSC C576818 @20000+ break (annual qty 30000)
196 | 2 | CTRL-C2000: 2 | 4.7u 50V | Capacitor 4.7u 50V X7R 1210 |  |  | 1210 | GENERIC |  | 0.148600 | 0.2972 | estimate class:mlcc_1210_x7r_50v_le10u: GENERIC class rule, reel price of a typical equivalent. LCSC C381467 FS32X106K500EGG (1210); US$0.1486 at 5000+; example is 10 uF 50 V; r... | high | 0.148600 | REAL: class example LCSC C381467 @5000+ break (annual qty 10000)
197 | 2 | SYS-IO-AUX: 2 | 4.7u 50V | Capacitor 4.7u 10% 50V X7R 1210 |  |  | 1210 | GENERIC |  | 0.148600 | 0.2972 | estimate class:mlcc_1210_x7r_50v_le10u: GENERIC class rule, reel price of a typical equivalent. LCSC C381467 FS32X106K500EGG (1210); US$0.1486 at 5000+; example is 10 uF 50 V; r... | high | 0.148600 | REAL: class example LCSC C381467 @5000+ break (annual qty 10000)
198 | 3 | DAB60: 3 | 4.7u 50V | Capacitor 4.7u 50V X7R 1206 |  |  | 1206 | GENERIC |  | 0.047100 | 0.1413 | estimate class:mlcc_1206_x7r_50v_le10u: GENERIC class rule, reel price of a typical equivalent. LCSC C51205 CL31B475KBHNNNE (1206); US$0.0471 at 4000+; example is 4.7 uF 50 V; r... | high | 0.046100 | REAL: class example LCSC C51205 @10000+ break (annual qty 15000)
199 | 1 | CTRL-C2000: 1 | 4.87k | Resistor 4.87k 1% 0603 |  |  | 0603 | GENERIC |  | 0.003000 | 0.0030 | estimate class:res_0603_1pct: GENERIC class rule, reel price of a typical equivalent. LCSC C2906982 FRC0603F1002TS (0603); US$0.003 at 5000+; 10 kOhm 1 %; read 2026-10... | high | 0.003000 | REAL: class example LCSC C2906982 @5000+ break (annual qty 5000)
200 | 8 | DAB60: 4; SYS-IO-AUX: 4 | 4.99k | Resistor 4.99k 1% 0603 |  |  | 0603 | GENERIC |  | 0.003000 | 0.0240 | estimate class:res_0603_1pct: GENERIC class rule, reel price of a typical equivalent. LCSC C2906982 FRC0603F1002TS (0603); US$0.003 at 5000+; 10 kOhm 1 %; read 2026-10... | high | 0.002900 | REAL: class example LCSC C2906982 @10000+ break (annual qty 40000)
201 | 1 | DAB60: 1 | 40.2k | Resistor 40.2k 0.1% 0603 board ID DAB60-B2 (interfaces.ID_OHM) |  |  | 0603 | GENERIC |  | 0.003900 | 0.0039 | estimate class:res_0603_0.1pct: GENERIC class rule, reel price of a typical equivalent. LCSC C5126214 FRH0603B1002TS (0603); US$0.0039 at 5000+; 10 kOhm 0.1 %; read 2026... | high | 0.003900 | REAL: class example LCSC C5126214 @5000+ break (annual qty 5000)
202 | 4 | DAB60: 4 | 402R | Resistor 402R 0.1% 0603 |  |  | 0603 | GENERIC |  | 0.003900 | 0.0156 | estimate class:res_0603_0.1pct: GENERIC class rule, reel price of a typical equivalent. LCSC C5126214 FRH0603B1002TS (0603); US$0.0039 at 5000+; 10 kOhm 0.1 %; read 2026... | high | 0.003500 | REAL: class example LCSC C5126214 @10000+ break (annual qty 20000)
203 | 2 | DAB60: 2 | 402k | Resistor 402k 0.1% 0603 hold readback |  |  | 0603 | GENERIC |  | 0.003900 | 0.0078 | estimate class:res_0603_0.1pct: GENERIC class rule, reel price of a typical equivalent. LCSC C5126214 FRH0603B1002TS (0603); US$0.0039 at 5000+; 10 kOhm 0.1 %; read 2026... | high | 0.003500 | REAL: class example LCSC C5126214 @10000+ break (annual qty 10000)
204 | 2 | DAB60: 2 | 412R | Resistor 412R 0.1% 0603 |  |  | 0603 | GENERIC |  | 0.003900 | 0.0078 | estimate class:res_0603_0.1pct: GENERIC class rule, reel price of a typical equivalent. LCSC C5126214 FRH0603B1002TS (0603); US$0.0039 at 5000+; 10 kOhm 0.1 %; read 2026... | high | 0.003500 | REAL: class example LCSC C5126214 @10000+ break (annual qty 10000)
205 | 1 | DAB60: 1 | 43.2k | Resistor 43.2k 1% 0603 |  |  | 0603 | GENERIC |  | 0.003000 | 0.0030 | estimate class:res_0603_1pct: GENERIC class rule, reel price of a typical equivalent. LCSC C2906982 FRC0603F1002TS (0603); US$0.003 at 5000+; 10 kOhm 1 %; read 2026-10... | high | 0.003000 | REAL: class example LCSC C2906982 @5000+ break (annual qty 5000)
206 | 25 | DAB60: 20; SYS-IO-AUX: 5 | 470R | Resistor 470R 1% 0603 |  |  | 0603 | GENERIC |  | 0.003000 | 0.0750 | estimate class:res_0603_1pct: GENERIC class rule, reel price of a typical equivalent. LCSC C2906982 FRC0603F1002TS (0603); US$0.003 at 5000+; 10 kOhm 1 %; read 2026-10... | high | 0.002800 | REAL: class example LCSC C2906982 @50200+ break (annual qty 125000)
207 | 1 | SYS-IO-AUX: 1 | 470p 2kV | Capacitor 470p 5% 2kV C0G 1206 |  |  | 1206 | GENERIC |  | 0.037600 | 0.0376 | estimate class:mlcc_1206_c0g_2kv_le1n: GENERIC class rule, reel price of a typical equivalent. LCSC C113876 CC1206JKNPODBN101 (1206); US$0.0376 at 3000+; nearest listed part is... | medium | 0.037600 | REAL: class example LCSC C113876 @3000+ break (annual qty 5000)
208 | 1 | AUX-HV_DAB: 1 | 470p 50V | Capacitor 470p 50V C0G 0603 |  |  | 0603 | GENERIC |  | 0.005500 | 0.0055 | estimate class:mlcc_0603_c0g_50v_le1n: GENERIC class rule, reel price of a typical equivalent. LCSC C14665 CC0603JRNPO9BN101 (0603); US$0.0055 at 4000+; example is 100 pF; read... | high | 0.005500 | REAL: class example LCSC C14665 @4000+ break (annual qty 5000)
209 | 20 | CTRL-C2000: 20 | 47R | Resistor 47R 1% 0603 |  |  | 0603 | GENERIC |  | 0.003000 | 0.0600 | estimate class:res_0603_1pct: GENERIC class rule, reel price of a typical equivalent. LCSC C2906982 FRC0603F1002TS (0603); US$0.003 at 5000+; 10 kOhm 1 %; read 2026-10... | high | 0.002800 | REAL: class example LCSC C2906982 @50200+ break (annual qty 100000)
210 | 12 | AUX-HV_DAB: 2; DAB60: 10 | 47k | Resistor 47k 1% 0603 |  |  | 0603 | GENERIC |  | 0.003000 | 0.0360 | estimate class:res_0603_1pct: GENERIC class rule, reel price of a typical equivalent. LCSC C2906982 FRC0603F1002TS (0603); US$0.003 at 5000+; 10 kOhm 1 %; read 2026-10... | high | 0.002800 | REAL: class example LCSC C2906982 @50200+ break (annual qty 60000)
211 | 2 | DAB60: 2 | 47k | Resistor 47k 1% 0603 DO line pull-down |  |  | 0603 | GENERIC |  | 0.003000 | 0.0060 | estimate class:res_0603_1pct: GENERIC class rule, reel price of a typical equivalent. LCSC C2906982 FRC0603F1002TS (0603); US$0.003 at 5000+; 10 kOhm 1 %; read 2026-10... | high | 0.002900 | REAL: class example LCSC C2906982 @10000+ break (annual qty 10000)
212 | 20 | DAB60: 20 | 47k | Resistor 47k 1% 2512 1 W thick film, >= 500 V working |  |  | 2512 | GENERIC |  | 0.025800 | 0.5160 | estimate class:res_2512_1pct: GENERIC class rule, reel price of a typical equivalent. LCSC C2934076 FRC2512F4702TS (2512); US$0.0258 at 4000+; 47 kOhm 1 W 1 %; read 20... | high | 0.023300 | REAL: class example LCSC C2934076 @20000+ break (annual qty 100000)
213 | 2 | DAB60: 2 | 47k | Resistor 47k 1% 0603 DIAG pull-up (SBASA11B Fig 7-5) |  |  | 0603 | GENERIC |  | 0.003000 | 0.0060 | estimate class:res_0603_1pct: GENERIC class rule, reel price of a typical equivalent. LCSC C2906982 FRC0603F1002TS (0603); US$0.003 at 5000+; 10 kOhm 1 %; read 2026-10... | high | 0.002900 | REAL: class example LCSC C2906982 @10000+ break (annual qty 10000)
214 | 1 | AUX-HV_DAB: 1 | 47n 50V | Capacitor 47n 50V X7R 0603 |  |  | 0603 | GENERIC |  | 0.009200 | 0.0092 | estimate class:mlcc_0603_x7r_50v_le100n: GENERIC class rule, reel price of a typical equivalent. LCSC C14663 CC0603KRX7R9BB104 (0603); US$0.0092 at 4000+; read 2026-10-04 via the... | high | 0.009200 | REAL: class example LCSC C14663 @4000+ break (annual qty 5000)
215 | 8 | CTRL-C2000: 4; DAB60: 4 | 49.9R | Resistor 49.9R 1% 0603 |  |  | 0603 | GENERIC |  | 0.003000 | 0.0240 | estimate class:res_0603_1pct: GENERIC class rule, reel price of a typical equivalent. LCSC C2906982 FRC0603F1002TS (0603); US$0.003 at 5000+; 10 kOhm 1 %; read 2026-10... | high | 0.002900 | REAL: class example LCSC C2906982 @10000+ break (annual qty 40000)
216 | 16 | DAB60: 16 | 49.9k | Resistor 49.9k 0.1% 0603 |  |  | 0603 | GENERIC |  | 0.003900 | 0.0624 | estimate class:res_0603_0.1pct: GENERIC class rule, reel price of a typical equivalent. LCSC C5126214 FRH0603B1002TS (0603); US$0.0039 at 5000+; 10 kOhm 0.1 %; read 2026... | high | 0.003300 | REAL: class example LCSC C5126214 @50000+ break (annual qty 80000)
217 | 1 | CTRL-C2000: 1 | 499R | Resistor 499R 0.1% 0603 10ppm/K |  |  | 0603 | GENERIC |  | 0.041000 | 0.0410 | estimate class:res_0603_0.1pct_10ppm: GENERIC class rule, reel price of a typical equivalent. LCSC C190610 ERA3AEB103V (0603); US$0.041 at 5000+; Panasonic ERA-3A thin film 0.... | medium | 0.041000 | REAL: class example LCSC C190610 @5000+ break (annual qty 5000)
218 | 1 | CTRL-C2000: 1 | 5.23k | Resistor 5.23k 0.1% 0603 10ppm/K |  |  | 0603 | GENERIC |  | 0.041000 | 0.0410 | estimate class:res_0603_0.1pct_10ppm: GENERIC class rule, reel price of a typical equivalent. LCSC C190610 ERA3AEB103V (0603); US$0.041 at 5000+; Panasonic ERA-3A thin film 0.... | medium | 0.041000 | REAL: class example LCSC C190610 @5000+ break (annual qty 5000)
219 | 1 | SYS-IO-AUX: 1 | 5.23k | Resistor 5.23k 0.1% 0603 10 ppm/K thin film |  |  | 0603 | GENERIC |  | 0.041000 | 0.0410 | estimate class:res_0603_0.1pct_10ppm: GENERIC class rule, reel price of a typical equivalent. LCSC C190610 ERA3AEB103V (0603); US$0.041 at 5000+; Panasonic ERA-3A thin film 0.... | medium | 0.041000 | REAL: class example LCSC C190610 @5000+ break (annual qty 5000)
220 | 16 | CTRL-C2000: 16 | 5.76k | Resistor 5.76k 0.1% 0603 10ppm/K |  |  | 0603 | GENERIC |  | 0.041000 | 0.6560 | estimate class:res_0603_0.1pct_10ppm: GENERIC class rule, reel price of a typical equivalent. LCSC C190610 ERA3AEB103V (0603); US$0.041 at 5000+; Panasonic ERA-3A thin film 0.... | medium | 0.038900 | REAL: class example LCSC C190610 @10000+ break (annual qty 80000)
221 | 1 | AUX-HV_DAB: 1 | 53.6k | Resistor 53.6k 0.1% 0603 |  |  | 0603 | GENERIC |  | 0.003900 | 0.0039 | estimate class:res_0603_0.1pct: GENERIC class rule, reel price of a typical equivalent. LCSC C5126214 FRH0603B1002TS (0603); US$0.0039 at 5000+; 10 kOhm 0.1 %; read 2026... | high | 0.003900 | REAL: class example LCSC C5126214 @5000+ break (annual qty 5000)
222 | 8 | CTRL-C2000: 8 | 560R | Resistor 560R 1% 0603 |  |  | 0603 | GENERIC |  | 0.003000 | 0.0240 | estimate class:res_0603_1pct: GENERIC class rule, reel price of a typical equivalent. LCSC C2906982 FRC0603F1002TS (0603); US$0.003 at 5000+; 10 kOhm 1 %; read 2026-10... | high | 0.002900 | REAL: class example LCSC C2906982 @10000+ break (annual qty 40000)
223 | 1 | AUX-HV_DAB: 1 | 560R | Resistor 560R 1% 0805 |  |  | 0805 | GENERIC |  | 0.001500 | 0.0015 | estimate class:res_0805_1pct: GENERIC class rule, reel price of a typical equivalent. LCSC C17878 0805W8F976JT5E (0805); US$0.0015 at 5000+; 97.6 Ohm 1 %; read 2026-10... | high | 0.001500 | REAL: class example LCSC C17878 @5000+ break (annual qty 5000)
224 | 9 | SYS-IO-AUX: 9 | 562R | Resistor 562R 1% 0603 |  |  | 0603 | GENERIC |  | 0.003000 | 0.0270 | estimate class:res_0603_1pct: GENERIC class rule, reel price of a typical equivalent. LCSC C2906982 FRC0603F1002TS (0603); US$0.003 at 5000+; 10 kOhm 1 %; read 2026-10... | high | 0.002900 | REAL: class example LCSC C2906982 @10000+ break (annual qty 45000)
225 | 1 | CTRL-C2000: 1 | 56R | Resistor 56R 1% 0805 |  |  | 0805 | GENERIC |  | 0.001500 | 0.0015 | estimate class:res_0805_1pct: GENERIC class rule, reel price of a typical equivalent. LCSC C17878 0805W8F976JT5E (0805); US$0.0015 at 5000+; 97.6 Ohm 1 %; read 2026-10... | high | 0.001500 | REAL: class example LCSC C17878 @5000+ break (annual qty 5000)
226 | 8 | CTRL-C2000: 8 | 56p 50V | Capacitor 56p 5% 50V C0G 0603 |  |  | 0603 | GENERIC |  | 0.005500 | 0.0440 | estimate class:mlcc_0603_c0g_50v_le1n: GENERIC class rule, reel price of a typical equivalent. LCSC C14665 CC0603JRNPO9BN101 (0603); US$0.0055 at 4000+; example is 100 pF; read... | high | 0.005300 | REAL: class example LCSC C14665 @8000+ break (annual qty 40000)
227 | 1 | AUX-HV_DAB: 1 | 59k | Resistor 59k 1% 0603 |  |  | 0603 | GENERIC |  | 0.003000 | 0.0030 | estimate class:res_0603_1pct: GENERIC class rule, reel price of a typical equivalent. LCSC C2906982 FRC0603F1002TS (0603); US$0.003 at 5000+; 10 kOhm 1 %; read 2026-10... | high | 0.003000 | REAL: class example LCSC C2906982 @5000+ break (annual qty 5000)
228 | 8 | DAB60: 8 | 6.04k | Resistor 6.04k 0.1% 0603 |  |  | 0603 | GENERIC |  | 0.003900 | 0.0312 | estimate class:res_0603_0.1pct: GENERIC class rule, reel price of a typical equivalent. LCSC C5126214 FRH0603B1002TS (0603); US$0.0039 at 5000+; 10 kOhm 0.1 %; read 2026... | high | 0.003500 | REAL: class example LCSC C5126214 @10000+ break (annual qty 40000)
229 | 1 | SYS-IO-AUX: 1 | 6.49k | Resistor 6.49k 0.1% 0603 10 ppm/K thin film |  |  | 0603 | GENERIC |  | 0.041000 | 0.0410 | estimate class:res_0603_0.1pct_10ppm: GENERIC class rule, reel price of a typical equivalent. LCSC C190610 ERA3AEB103V (0603); US$0.041 at 5000+; Panasonic ERA-3A thin film 0.... | medium | 0.041000 | REAL: class example LCSC C190610 @5000+ break (annual qty 5000)
230 | 6 | BMU-GW: 2; SYS-IO-AUX: 4 | 60.4R | Resistor 60.4R 1% 0805 |  |  | 0805 | GENERIC |  | 0.001500 | 0.0090 | estimate class:res_0805_1pct: GENERIC class rule, reel price of a typical equivalent. LCSC C17878 0805W8F976JT5E (0805); US$0.0015 at 5000+; 97.6 Ohm 1 %; read 2026-10... | high | 0.001400 | REAL: class example LCSC C17878 @10000+ break (annual qty 30000)
231 | 1 | AUX-HV_DAB: 1 | 619k | Resistor 619k 0.1% 0603 |  |  | 0603 | GENERIC |  | 0.003900 | 0.0039 | estimate class:res_0603_0.1pct: GENERIC class rule, reel price of a typical equivalent. LCSC C5126214 FRH0603B1002TS (0603); US$0.0039 at 5000+; 10 kOhm 0.1 %; read 2026... | high | 0.003900 | REAL: class example LCSC C5126214 @5000+ break (annual qty 5000)
232 | 4 | DAB60: 4 | 620p 50V | Capacitor 620p 5% 50V C0G 0603 |  |  | 0603 | GENERIC |  | 0.005500 | 0.0220 | estimate class:mlcc_0603_c0g_50v_le1n: GENERIC class rule, reel price of a typical equivalent. LCSC C14665 CC0603JRNPO9BN101 (0603); US$0.0055 at 4000+; example is 100 pF; read... | high | 0.005300 | REAL: class example LCSC C14665 @8000+ break (annual qty 20000)
233 | 1 | CTRL-C2000: 1 | 64.9k | Resistor 64.9k 1% 0603 |  |  | 0603 | GENERIC |  | 0.003000 | 0.0030 | estimate class:res_0603_1pct: GENERIC class rule, reel price of a typical equivalent. LCSC C2906982 FRC0603F1002TS (0603); US$0.003 at 5000+; 10 kOhm 1 %; read 2026-10... | high | 0.003000 | REAL: class example LCSC C2906982 @5000+ break (annual qty 5000)
234 | 8 | DAB60: 8 | 66.5k | Resistor 66.5k 0.1% 0603 |  |  | 0603 | GENERIC |  | 0.003900 | 0.0312 | estimate class:res_0603_0.1pct: GENERIC class rule, reel price of a typical equivalent. LCSC C5126214 FRH0603B1002TS (0603); US$0.0039 at 5000+; 10 kOhm 0.1 %; read 2026... | high | 0.003500 | REAL: class example LCSC C5126214 @10000+ break (annual qty 40000)
235 | 4 | CTRL-C2000: 4 | 680R | Resistor 680R 1% 0603 |  |  | 0603 | GENERIC |  | 0.003000 | 0.0120 | estimate class:res_0603_1pct: GENERIC class rule, reel price of a typical equivalent. LCSC C2906982 FRC0603F1002TS (0603); US$0.003 at 5000+; 10 kOhm 1 %; read 2026-10... | high | 0.002900 | REAL: class example LCSC C2906982 @10000+ break (annual qty 20000)
236 | 4 | CTRL-C2000: 4 | 680n 50V | Capacitor 680n 10% 50V X7R 0603 |  |  | 0603 | GENERIC |  | 0.009100 | 0.0364 | estimate class:mlcc_0603_x7r_50v_le1u: GENERIC class rule, reel price of a typical equivalent. LCSC C64705 CL10B224KB8NNNC (0603); US$0.0091 at 4000+; example is 220 nF; read 2... | high | 0.008600 | REAL: class example LCSC C64705 @8000+ break (annual qty 20000)
237 | 1 | AUX-HV_DAB: 1 | 68n 50V | Capacitor 68n 5% 50V C0G 1206 |  |  | 1206 | GENERIC |  | 0.136200 | 0.1362 | estimate class:mlcc_1206_c0g_50v_le100n: GENERIC class rule, reel price of a typical equivalent. LCSC C97946 GRM31C5C1H104JA01L (1206); US$0.1362 at 4000+; example is 100 nF 50 V... | high | 0.136200 | REAL: class example LCSC C97946 @4000+ break (annual qty 5000)
238 | 1 | AUX-HV_DAB: 1 | 68p 500V | Capacitor 68p 500V C0G 1206 |  |  | 1206 | GENERIC |  | 0.025300 | 0.0253 | estimate class:mlcc_1206_c0g_630v_le1n: GENERIC class rule, reel price of a typical equivalent. LCSC C107178 CC1206JKNPOCBN680 (1206); US$0.0253 at 3000+; example is 68 pF rated... | medium | 0.025300 | REAL: class example LCSC C107178 @3000+ break (annual qty 5000)
239 | 2 | DAB60: 2 | 7.32k | Resistor 7.32k 1% 0603 R_PXFR: two-wire EN current 1.9 mA (SLVSFJ7D table 8-2) |  |  | 0603 | GENERIC |  | 0.003000 | 0.0060 | estimate class:res_0603_1pct: GENERIC class rule, reel price of a typical equivalent. LCSC C2906982 FRC0603F1002TS (0603); US$0.003 at 5000+; 10 kOhm 1 %; read 2026-10... | high | 0.002900 | REAL: class example LCSC C2906982 @10000+ break (annual qty 10000)
240 | 4 | DAB60: 4 | 7.87k | Resistor 7.87k 0.1% 0603 |  |  | 0603 | GENERIC |  | 0.003900 | 0.0156 | estimate class:res_0603_0.1pct: GENERIC class rule, reel price of a typical equivalent. LCSC C5126214 FRH0603B1002TS (0603); US$0.0039 at 5000+; 10 kOhm 0.1 %; read 2026... | high | 0.003500 | REAL: class example LCSC C5126214 @10000+ break (annual qty 20000)
241 | 1 | CTRL-C2000: 1 | 732R | Resistor 732R 0.1% 0603 10ppm/K |  |  | 0603 | GENERIC |  | 0.041000 | 0.0410 | estimate class:res_0603_0.1pct_10ppm: GENERIC class rule, reel price of a typical equivalent. LCSC C190610 ERA3AEB103V (0603); US$0.041 at 5000+; Panasonic ERA-3A thin film 0.... | medium | 0.041000 | REAL: class example LCSC C190610 @5000+ break (annual qty 5000)
242 | 4 | CTRL-C2000: 4 | 8.06k | Resistor 8.06k 1% 0603 |  |  | 0603 | GENERIC |  | 0.003000 | 0.0120 | estimate class:res_0603_1pct: GENERIC class rule, reel price of a typical equivalent. LCSC C2906982 FRC0603F1002TS (0603); US$0.003 at 5000+; 10 kOhm 1 %; read 2026-10... | high | 0.002900 | REAL: class example LCSC C2906982 @10000+ break (annual qty 20000)
243 | 1 | SYS-IO-AUX: 1 | 8.06k | Resistor 8.06k 0.1% 0603 |  |  | 0603 | GENERIC |  | 0.003900 | 0.0039 | estimate class:res_0603_0.1pct: GENERIC class rule, reel price of a typical equivalent. LCSC C5126214 FRH0603B1002TS (0603); US$0.0039 at 5000+; 10 kOhm 0.1 %; read 2026... | high | 0.003900 | REAL: class example LCSC C5126214 @5000+ break (annual qty 5000)
244 | 2 | DAB60: 2 | 81.6k | Resistor 81.6k 0.1% 0603 |  |  | 0603 | GENERIC |  | 0.003900 | 0.0078 | estimate class:res_0603_0.1pct: GENERIC class rule, reel price of a typical equivalent. LCSC C5126214 FRH0603B1002TS (0603); US$0.0039 at 5000+; 10 kOhm 0.1 %; read 2026... | high | 0.003500 | REAL: class example LCSC C5126214 @10000+ break (annual qty 10000)
245 | 24 | DAB60: 24 | 82.5k | Resistor 82.5k 1% 2512 monitor loop, <= 300 V per element in an In surge |  |  | 2512 | GENERIC |  | 0.025800 | 0.6192 | estimate class:res_2512_1pct: GENERIC class rule, reel price of a typical equivalent. LCSC C2934076 FRC2512F4702TS (2512); US$0.0258 at 4000+; 47 kOhm 1 W 1 %; read 20... | high | 0.023300 | REAL: class example LCSC C2934076 @20000+ break (annual qty 120000)
246 | 12 | CTRL-C2000: 12 | 82p 50V | Capacitor 82p 5% 50V C0G 0603 |  |  | 0603 | GENERIC |  | 0.005500 | 0.0660 | estimate class:mlcc_0603_c0g_50v_le1n: GENERIC class rule, reel price of a typical equivalent. LCSC C14665 CC0603JRNPO9BN101 (0603); US$0.0055 at 4000+; example is 100 pF; read... | high | 0.005100 | REAL: class example LCSC C14665 @48200+ break (annual qty 60000)
247 | 8 | DAB60: 8 | 86.6k | Resistor 86.6k 0.1% 0603 proof-test injection |  |  | 0603 | GENERIC |  | 0.003900 | 0.0312 | estimate class:res_0603_0.1pct: GENERIC class rule, reel price of a typical equivalent. LCSC C5126214 FRH0603B1002TS (0603); US$0.0039 at 5000+; 10 kOhm 0.1 %; read 2026... | high | 0.003500 | REAL: class example LCSC C5126214 @10000+ break (annual qty 40000)
248 | 8 | DAB60: 8 | 88.7k | Resistor 88.7k 0.1% 0603 |  |  | 0603 | GENERIC |  | 0.003900 | 0.0312 | estimate class:res_0603_0.1pct: GENERIC class rule, reel price of a typical equivalent. LCSC C5126214 FRH0603B1002TS (0603); US$0.0039 at 5000+; 10 kOhm 0.1 %; read 2026... | high | 0.003500 | REAL: class example LCSC C5126214 @10000+ break (annual qty 40000)
249 | 1 | SYS-IO-AUX: 1 | 9.09k | Resistor 9.09k 1% 0603 |  |  | 0603 | GENERIC |  | 0.003000 | 0.0030 | estimate class:res_0603_1pct: GENERIC class rule, reel price of a typical equivalent. LCSC C2906982 FRC0603F1002TS (0603); US$0.003 at 5000+; 10 kOhm 1 %; read 2026-10... | high | 0.003000 | REAL: class example LCSC C2906982 @5000+ break (annual qty 5000)
250 | 2 | DAB60: 2 | 909R | Resistor 909R 0.1% 0603 |  |  | 0603 | GENERIC |  | 0.003900 | 0.0078 | estimate class:res_0603_0.1pct: GENERIC class rule, reel price of a typical equivalent. LCSC C5126214 FRH0603B1002TS (0603); US$0.0039 at 5000+; 10 kOhm 0.1 %; read 2026... | high | 0.003500 | REAL: class example LCSC C5126214 @10000+ break (annual qty 10000)
251 | 1 | SYS-IO-AUX: 1 | 95.3k | Resistor 95.3k 1% 0603 |  |  | 0603 | GENERIC |  | 0.003000 | 0.0030 | estimate class:res_0603_1pct: GENERIC class rule, reel price of a typical equivalent. LCSC C2906982 FRC0603F1002TS (0603); US$0.003 at 5000+; 10 kOhm 1 %; read 2026-10... | high | 0.003000 | REAL: class example LCSC C2906982 @5000+ break (annual qty 5000)
252 | 1 | SYS-IO-AUX: 1 | Chassis (PE) bonding mounting hole | Chassis (PE) bonding mounting hole |  |  | M3 plated hole | NOPART |  | 0.000000 | 0.0000 | not a purchased part |  | 0.000000 | not a purchased part
253 | 1 | CTRL-C2000: 1 | Net tie: single AGND-GND star point | Net tie: single AGND-GND star point |  |  | net tie | NOPART |  | 0.000000 | 0.0000 | not a purchased part |  | 0.000000 | not a purchased part
254 | 1 | DAB60: 1 | PE bond M4 | PE bond: plated M4 mounting hole + serrated washer to chassis PE |  |  | plated M4 hole | NOPART |  | 0.000000 | 0.0000 | not a purchased part |  | 0.000000 | not a purchased part
255 | 8 | BMU-GW: 2; CTRL-C2000: 2; SYS-IO-AUX: 4 | Solder jumper, open by default | Solder jumper, open by default |  |  | solder jumper | NOPART |  | 0.000000 | 0.0000 | not a purchased part |  | 0.000000 | not a purchased part
256 | 66 | AUX-HV_DAB: 5; CTRL-C2000: 23; DAB60: 11; SYS-IO-AUX: 27 | TP | Test point |  |  | TP | NOPART |  | 0.000000 | 0.0000 | not a purchased part |  | 0.000000 | not a purchased part
257 | 2 | CTRL-C2000: 2 | ASDMB-25.000MHZ-XC-T | MEMS oscillator 25.000 MHz CMOS, 3.3 V, +/-50 ppm, -40..105 C | Abracon | ASDMB-25.000MHZ-XC-T | 2.5x2.0 mm 4-pad | ORDERABLE | docs/datasheets/timing/ASDMB.pdf | 1.720000 | 3.4400 | estimate ASDMB-25.000MHZ-XC-T: ESTIMATE: no listing of the -XC-T option; the same Abracon ASDMB 25.000 MHz family in -LC-T is 1.7164 USD at 1000+ on LCSC (C2650748, mir... | medium | 1.462000 | ASSUMED x0.85 [asia_part_estimate]
258 | 3 | BMU-GW: 1; SYS-IO-AUX: 2 | CDSOT23-SM712 | RS-485 asymmetric TVS array, -7 V / +12 V working | Bourns | CDSOT23-SM712 | SOT-23 | ORDERABLE | docs/datasheets/protection/CDSOT23-SM712.pdf | 0.276600 | 0.8298 | LCSC C404012 @1000+ (2026-10-04) | high | 0.276600 | REAL: LCSC C404012 @1000+ break (annual qty 15000)
259 | 2 | DAB60: 2 | CSM2F-8518-L100J01 | BUSBAR-MOUNTED shunt 100 uOhm 5 % 36 W, Kelvin test points (pins 3/4) | Bourns | CSM2F-8518-L100J01 | busbar shunt 85x18 mm | ORDERABLE | docs/datasheets/sensing/CSM2F-8518.pdf | 16.570000 | 33.1400 | DigiKey (web-search snippet; page blocked) 9487207 @100+ (2026-10-04) | medium | 14.084500 | ASSUMED x0.85 [short_table]
260 | 3 | SYS-IO-AUX: 3 | SF-2923HC30C-2 | Fuse 30 A 60 VDC, 300 A interrupting, single blow | Bourns | SF-2923HC30C-2 | 2923 SMD | ORDERABLE | docs/datasheets/protection/SF-2923HC.pdf | 1.200000 | 3.6000 | estimate SF-2923HC30C-2: ESTIMATE: Bourns SF-2923 30 A 60 VDC SMD fuse, no readable price (not on LCSC through the mirror); engineering estimate for a 2923 high-c... | low | 0.960000 | ASSUMED x0.80 [protection_estimate]
261 | 8 | SYS-IO-AUX: 8 | SMAJ12A | TVS unidirectional 400 W, VRWM 12 V, VBR 13.3-14.7 V | Bourns | SMAJ12A | DO-214AC (SMA) | ORDERABLE | docs/datasheets/protection/SMAJ_Bourns.pdf | 0.028800 | 0.2304 | LCSC C113957 @600+ (2026-10-04) | high | 0.019700 | REAL: LCSC C113957 @20000+ break (annual qty 40000)
262 | 4 | SYS-IO-AUX: 4 | SMAJ33A | TVS unidirectional 400 W, VRWM 33 V, VBR 36.7-40.6 V | Bourns | SMAJ33A | DO-214AC (SMA) | ORDERABLE | docs/datasheets/protection/SMAJ_Bourns.pdf | 0.021800 | 0.0872 | LCSC C908777 @600+ (2026-10-04) | high | 0.016600 | REAL: LCSC C908777 @16000+ break (annual qty 20000)
263 | 8 | SYS-IO-AUX: 8 | SMAJ36A | TVS unidirectional 400 W, VRWM 36 V, VBR 40-44.2 V | Bourns | SMAJ36A | DO-214AC (SMA) | ORDERABLE | docs/datasheets/protection/SMAJ_Bourns.pdf | 0.029000 | 0.2320 | LCSC C113967 @600+ (2026-10-04) | high | 0.020100 | REAL: LCSC C113967 @20000+ break (annual qty 40000)
264 | 2 | DAB60: 2 | SMBJ33A | TVS 33 V unidirectional, relay coil clamp zener | Bourns | SMBJ33A | SMB | ORDERABLE | docs/datasheets/protection/SMBJ_Bourns.pdf | 0.045100 | 0.0902 | LCSC C173526 @1000+ (2026-10-05) | high | 0.028800 | REAL: LCSC C173526 @9000+ break (annual qty 10000)
265 | 3 | SYS-IO-AUX: 3 | SMCJ33CA | TVS bidirectional 1500 W, VRWM 33 V, VC 53.3 V | Bourns | SMCJ33CA | DO-214AB (SMC) | ORDERABLE | docs/datasheets/protection/SMCJ_Bourns.pdf | 0.169700 | 0.5091 | LCSC C224050 @500+ (2026-10-04) | high | 0.124700 | REAL: LCSC C224050 @6000+ break (annual qty 15000)
266 | 3 | AUX-HV_DAB: 3 | SMCJ70A | TVS unidirectional 1500 W, VRWM 70 V, VBR 77.8-86.0 V (clamp, 3 in series) | Bourns | SMCJ70A | DO-214AB (SMC) | ORDERABLE | docs/datasheets/protection/SMCJ_Bourns.pdf |  |  | UNPRICED | none |  | UNPRICED
267 | 1 | BMU-GW: 1 | KF2EDGR-3.81-6P | Pluggable header 6-pos 3.81 mm right angle, 300 V 8 A, -40..+105 C, BMS field wiring (plug KF2EDGK-3.81-6P) | Cixi Kefa Electronic | KF2EDGR-3.81-6P | pluggable header 6-pos 3.81 mm | ORDERABLE | docs/datasheets/connectors/KEFA-KF2EDGR-3.81.pdf | 0.079800 | 0.0798 | LCSC C441186 @500+ (2026-10-04) | high | 0.066300 | REAL: LCSC C441186 @5000+ break (annual qty 5000)
268 | 2 | DAB60: 2 | MMBT3904-7-F | NPN 40 V 200 mA | Diodes Inc | MMBT3904-7-F | SOT-23 | ORDERABLE | docs/datasheets/power-semiconductors/MMBT3904.pdf | 0.024300 | 0.0486 | LCSC C94514 @600+ (2026-10-04) | high | 0.019600 | REAL: LCSC C94514 @9000+ break (annual qty 10000)
269 | 4 | DAB60: 4 | MMBT3906-7-F | PNP 40 V 200 mA | Diodes Inc | MMBT3906-7-F | SOT-23 | ORDERABLE | docs/datasheets/power-semiconductors/MMBT3906.pdf | 0.018400 | 0.0736 | LCSC C82762 @600+ (2026-10-04) | high | 0.015100 | REAL: LCSC C82762 @9000+ break (annual qty 20000)
270 | 6 | DAB60: 6 | S2M-13-F | Rectifier 1000 V 1.5 A | Diodes Inc | S2M-13-F | SMB | ORDERABLE | docs/datasheets/power-semiconductors/S2M.pdf | 0.055500 | 0.3330 | LCSC C156322 @500+ (2026-10-04) | high | 0.047700 | REAL: LCSC C156322 @6000+ break (annual qty 30000)
271 | 2 | SYS-IO-AUX: 2 | BAT54C-7-F | Dual common-cathode Schottky 30 V 200 mA | Diodes Incorporated | BAT54C-7-F | SOT-23 | ORDERABLE | docs/datasheets/protection/BAT54S-Diodes.pdf | 0.090800 | 0.1816 | LCSC C134405 @500+ (2026-10-04) | high | 0.069200 | REAL: LCSC C134405 @6000+ break (annual qty 10000)
272 | 21 | CTRL-C2000: 21 | BAT54S-7-F | Dual series Schottky 30 V 200 mA (ADC input clamp) | Diodes Incorporated | BAT54S-7-F | SOT-23 | ORDERABLE | docs/datasheets/protection/BAT54S-Diodes.pdf | 0.028000 | 0.5880 | LCSC C83574 @600+ (2026-10-04) | high | 0.020200 | REAL: LCSC C83574 @21000+ break (annual qty 105000)
273 | 5 | SYS-IO-AUX: 5 | BAT54S-7-F | Dual series Schottky 30 V 200 mA, input clamp to 3V3/GND | Diodes Incorporated | BAT54S-7-F | SOT-23 | ORDERABLE | docs/datasheets/protection/BAT54S-Diodes.pdf | 0.028000 | 0.1400 | LCSC C83574 @600+ (2026-10-04) | high | 0.020200 | REAL: LCSC C83574 @21000+ break (annual qty 25000)
274 | 3 | AUX-HV_DAB: 3 | US1G-13-F | Ultrafast rectifier 400 V 1 A | Diodes Incorporated | US1G-13-F | SMA | ORDERABLE | docs/datasheets/power-semiconductors/US1M.pdf | 0.053200 | 0.1596 | LCSC C110531 @500+ (2026-10-04) | high | 0.044500 | REAL: LCSC C110531 @5000+ break (annual qty 15000)
275 | 24 | DAB60: 24 | US1M-13-F | Ultrafast rectifier 1000 V 1 A trr 75 ns (DESAT string) | Diodes Incorporated | US1M-13-F | SMA | ORDERABLE | docs/datasheets/power-semiconductors/US1M.pdf | 0.036200 | 0.8688 | LCSC C99333 @1000+ (2026-10-04) | high | 0.029500 | REAL: LCSC C99333 @10000+ break (annual qty 120000)
276 | 4 | DAB60: 4 | 36A gPV 14x51 | Varistor branch fuse CH14x51 gPV 36 A 1000 V DC, 30 kA (L/R 2 ms), pre-arc 450 A2s | ETI | 002637115 | 14x51 cartridge in 2 x CH14-PCB clips | ORDERABLE | docs/datasheets/protection/ETI-Green-Protect.pdf | 6.000000 | 24.0000 | estimate 002637115: ESTIMATE: ETI CH14x51 gPV 36 A 1000 V d.c. fuse link (varistor branch fuse); ETI publishes no prices; engineering estimate for a 14x51 PV... | low | 4.800000 | ASSUMED x0.80 [protection_estimate]
277 | 8 | DAB60: 8 | 006710340 | Fuse clip CH14-PCB (two per varistor branch fuse) | ETI | 006710340 | PCB clip for 14 mm cartridge | ORDERABLE | docs/datasheets/protection/ETI-Green-Protect.pdf | 0.400000 | 3.2000 | estimate 006710340: ESTIMATE: ETI CH14-PCB fuse clip, no price found; engineering estimate for a plated PCB fuse clip | low | 0.320000 | ASSUMED x0.80 [protection_estimate]
278 | 3 | AUX-HV_DAB: 3 | BSS126H6327XTSA2 | N-MOSFET 600 V depletion mode, IDSS >= 7 mA (HV start-up cascode) | Infineon | BSS126H6327XTSA2 | SOT-23 | ORDERABLE | docs/datasheets/power-semiconductors/BSS126.pdf | 0.125600 | 0.3768 | LCSC C534596 @500+ (2026-10-04) | high | 0.111800 | REAL: LCSC C534596 @6000+ break (annual qty 15000)
279 | 1 | SYS-IO-AUX: 1 | FM24CL64B-GTR | F-RAM 64 kbit I2C, 1e14 write cycles | Infineon | FM24CL64B-GTR | SOIC-8 | ORDERABLE | docs/datasheets/controllers/FM24CL64B.pdf | 0.862300 | 0.8623 | LCSC C9829 @1000+ (2026-10-04) | high | 0.862300 | REAL: LCSC C9829 @1000+ break (annual qty 5000)
280 | 2 | DAB60: 2 | DD600N16K | CHASSIS-MOUNTED dual rectifier diode module 1600 V 600 A, one arm used as DC-link reverse clamp | Infineon Technologies Bipolar | DD600N16K | 60 mm industrial module, insulated base plate, screw terminals (12 Nm) | ORDERABLE | docs/datasheets/power-semiconductors/DD600N16K.pdf | 392.360000 | 784.7200 | Cytech Systems (web-search snippet) DD600N16KHPSA3 @100+ (2026-10-04) | medium | 333.506000 | ASSUMED x0.85 [short_table]
281 | 1 | AUX-HV_DAB: 1 | IV2Q171R0D7Z | SiC MOSFET 1700 V 1 Ohm, Kelvin source, AEC-Q101; alternate Sichain SG2M1K0170J2J (same pin-out) | InventChip | IV2Q171R0D7Z | TO-263-7 | ORDERABLE | docs/datasheets/power-semiconductors/IV2Q171R0D7Z.pdf | 2.500000 | 2.5000 | estimate IV2Q171R0D7Z: ESTIMATE (sim/out/aux_hv_design/aux75_block_cost.csv; architect's list 2.50): InventChip 1700 V 1 Ohm SiC MOSFET, not on LCSC, no public... | low | 2.125000 | ASSUMED x0.85 [asia_part_estimate]
282 | 2 | AUX-HV_DAB: 2 | 3.3u 1300V | Film capacitor 3.3 uF 1300 VDC, PP DC link, IEC 61071 (input surge absorber); was KEMET C4AQUBU4330A11J | Jianghai | FCSA3DS335K050ID90BE3 | radial 27.5 mm, 2 pins 5.0 mm, 32 x 28 x 18 mm | ORDERABLE | docs/datasheets/passives-capacitors/Jianghai-JE26-Film.pdf | 1.500000 | 3.0000 | estimate FCSA3DS335K050ID90BE3: ESTIMATE (sim/out/aux_hv_design/aux75_block_cost.csv): Jianghai 3.3 uF 1300 VDC film (input surge absorber), scaled from the 2.2 uF estimate | low | 1.275000 | ASSUMED x0.85 [asia_part_estimate]
283 | 3 | AUX-HV_DAB: 3 | PCV1HVF101MB12FV-WE3 | Aluminium polymer capacitor 100 uF 50 V, ESR 25 mOhm, 3.8 A, 3000 h @ 105 C (JE26 p17); was Wurth 875115655003 | Jianghai | PCV1HVF101MB12FV-WE3 | SMD V-chip 8.0 x 12.2 mm | ORDERABLE | docs/datasheets/passives-capacitors/Jianghai-JE26-Polymer.pdf | 0.300000 | 0.9000 | estimate PCV1HVF101MB12FV-WE3: ESTIMATE (sim/out/aux_hv_design/aux75_block_cost.csv 0.30): Jianghai polymer 100 uF 50 V, not in the mirror; the 35 V sibling PCR1VPF101M... | low | 0.255000 | ASSUMED x0.85 [asia_part_estimate]
284 | 3 | DAB60: 3 | C4AQQEW5650A3BJ | DC-link PP film 65 uF, 1100 VDC at 70 C hot spot (900 V at 85 C, 700 V at 105 C), ESR 2.6 mOhm, Irms 37.0 A (10 kHz, dT 30 K) | KEMET | C4AQQEW5650A3BJ | radial box 57.5 x 45 x 65 mm, 4 leads (S 52.5, S1 20.3) | ORDERABLE | docs/datasheets/passives-capacitors/C4AQ.pdf | 12.030000 | 36.0900 | estimate C4AQQEW5650A3BJ: ESTIMATE: KEMET C4AQ 65 uF 1100 V has the same 57.5x45x65 mm case as the 45 uF 1300 V C4AQUEW5450A3BJ, which is USD 12.03 at 100+ at the... | low | 10.225500 | ASSUMED x0.85 [asia_part_estimate]
285 | 3 | DAB60: 3 | C4AQUEW5450A3BJ | DC-link PP film 45 uF, 1300 VDC at 70 C hot spot (1100 V at 85 C, 850 V at 105 C), ESR 3.1 mOhm, Irms 34.0 A (10 kHz, dT 30 K) | KEMET | C4AQUEW5450A3BJ | radial box 57.5 x 45 x 65 mm, 4 leads (S 52.5, S1 20.3) | ORDERABLE | docs/datasheets/passives-capacitors/C4AQ.pdf | 10.870000 | 32.6100 | Dasenic broker (web-search snippet) C4AQUEW5450A3BJ @500+ (2026-10-04) | medium | 9.239500 | ASSUMED x0.85 [short_table]
286 | 2 | DAB60: 2 | HOB 130-P | Open-loop Hall current transducer DC-1 MHz, IPN 130 A rms, IPM +/-250 A, 8 mV/A on Uref 2.5 V, tD90 <= 200 ns; insulation basic 1000 V (p4) - used inside HV1/HV2, secondary on the bridge DC- | LEM | HOB 130-P | THT 38 x 22 mm, primary jumper 60 uOhm | ORDERABLE | docs/datasheets/sensing/HOB-P_series.pdf | 26.770000 | 53.5400 | Mouser Singapore (web-search snippet; page blocked) HOB 130-P @1+ (2026-10-04) single-piece price | medium | 13.920400 | ASSUMED x0.52 [single_piece_list]
287 | 1 | SYS-IO-AUX: 1 | LPJ4012AHNL | RJ45 10/100BASE-T, integrated magnetics and LEDs, -40..+85 C, 1500 Vrms hipot | LINK-PP | LPJ4012AHNL | RJ45 THT tab down, 1:1 magnetics, 2 LEDs | ORDERABLE | docs/datasheets/connectors/LINK-PP-LPJ4012AHNL.pdf |  |  | UNPRICED | none |  | UNPRICED
288 | 4 | DAB60: 4 | HP10NH1GPV160 | CHASSIS-MOUNTED fuse link gPV 1000 VDC 160 A NH1 (135 A port; base HPBB11PPR, Uimp 8 kV; inlet air path; 135 A to 45 C inlet, then the firmware current limit) | Mersen | HP10NH1GPV160 | NH1 blade, in base HPBB11PPR | ORDERABLE | docs/datasheets/protection/NH-gPV-1000VDC.pdf | 123.500000 | 494.0000 | estimate HP10NH1GPV160: ESTIMATE: no public price for the Mersen part; Siemens 3NE1224-4 (NH1, gPV, 160 A, 1000 V DC, same class) EUR 110.02 at Buerklin = USD 12... | low | 98.800000 | ASSUMED x0.80 [protection_estimate]
289 | 1 | CTRL-C2000: 1 | 24LC256T-I/SN | 256 kbit I2C EEPROM, 400 kHz, hardware write protect | Microchip | 24LC256T-I/SN | SOIC-8 (SN) | ORDERABLE | docs/datasheets/controllers/24LC256.pdf | 0.249000 | 0.2490 | LCSC C5458 @1000+ (2026-10-04) | high | 0.249000 | REAL: LCSC C5458 @1000+ break (annual qty 5000)
290 | 2 | SYS-IO-AUX: 2 | MCP23S17T-E/SS | 16-bit SPI I/O expander | Microchip | MCP23S17T-E/SS | SSOP-28 | ORDERABLE | docs/datasheets/controllers/MCP23S17.pdf | 0.846000 | 1.6920 | LCSC C128577 @1000+ (2026-10-04) | high | 0.846000 | REAL: LCSC C128577 @1000+ break (annual qty 10000)
291 | 8 | DAB60: 8 | 2N7002BK | N-MOSFET 60 V 350 mA logic level | Nexperia | 2N7002BK | SOT-23 | ORDERABLE | docs/datasheets/power-semiconductors/2N7002BK.pdf | 0.026500 | 0.2120 | LCSC C282405 @1000+ (2026-10-05) | high | 0.026500 | REAL: LCSC C282405 @1000+ break (annual qty 40000)
292 | 7 | SYS-IO-AUX: 7 | 2N7002BK,215 | N-MOSFET 60 V 350 mA, fan PWM open-drain driver | Nexperia | 2N7002BK,215 | SOT-23 | ORDERABLE | docs/datasheets/power-semiconductors/2N7002BK.pdf | 0.026500 | 0.1855 | LCSC C282405 @1000+ (2026-10-05) | high | 0.026400 | REAL: LCSC C282405 @9000+ break (annual qty 35000)
293 | 4 | AUX-HV_DAB: 4 | 2N7002BK,215 | N-MOSFET 60 V 350 mA (logic switch) | Nexperia | 2N7002BK,215 | SOT-23 | ORDERABLE | docs/datasheets/power-semiconductors/2N7002BK.pdf | 0.026500 | 0.1060 | LCSC C282405 @1000+ (2026-10-05) | high | 0.026400 | REAL: LCSC C282405 @9000+ break (annual qty 20000)
294 | 8 | DAB60: 8 | BAS16 | Switching diode 100 V 215 mA, low leakage | Nexperia | BAS16 | SOT-23 | ORDERABLE | docs/datasheets/protection/BAS16.pdf | 0.007800 | 0.0624 | LCSC C79997 @1000+ (2026-10-05) | high | 0.007800 | REAL: LCSC C79997 @1000+ break (annual qty 40000)
295 | 1 | AUX-HV_DAB: 1 | BAS16,215 | Switching diode 100 V 215 mA, low leakage (timer latch) | Nexperia | BAS16,215 | SOT-23 | ORDERABLE | docs/datasheets/protection/BAS16.pdf | 0.007800 | 0.0078 | LCSC C79997 @1000+ (2026-10-05) | high | 0.007800 | REAL: LCSC C79997 @1000+ break (annual qty 5000)
296 | 16 | DAB60: 16 | BAT54 | Schottky diode 30 V 200 mA, trr <= 5 ns | Nexperia | BAT54 | SOT-23 | ORDERABLE | docs/datasheets/protection/BAT54.pdf | 0.014300 | 0.2288 | LCSC C85084 @1000+ (2026-10-05) | high | 0.014300 | REAL: LCSC C85084 @1000+ break (annual qty 80000)
297 | 3 | AUX-HV_DAB: 3 | BAT54,215 | Schottky diode 30 V 200 mA | Nexperia | BAT54,215 | SOT-23 | ORDERABLE | docs/datasheets/protection/BAT54.pdf | 0.014300 | 0.0429 | LCSC C85084 @1000+ (2026-10-05) | high | 0.014300 | REAL: LCSC C85084 @1000+ break (annual qty 15000)
298 | 8 | DAB60: 8 | BAT54S | Dual series Schottky 30 V 200 mA (sense-node clamp to COM and VDD) | Nexperia | BAT54S | SOT-23 | ORDERABLE | docs/datasheets/protection/BAT54S.pdf | 0.019900 | 0.1592 | LCSC C47546 @1000+ (2026-10-05) | high | 0.019900 | REAL: LCSC C47546 @1000+ break (annual qty 40000)
299 | 1 | AUX-HV_DAB: 1 | BAT54S,215 | Dual series Schottky 30 V (soft start: clamp + discharge) | Nexperia | BAT54S,215 | SOT-23 | ORDERABLE | docs/datasheets/protection/BAT54S.pdf | 0.019900 | 0.0199 | LCSC C47546 @1000+ (2026-10-05) | high | 0.019900 | REAL: LCSC C47546 @1000+ break (annual qty 5000)
300 | 1 | AUX-HV_DAB: 1 | BC817-25,215 | NPN 45 V 500 mA (VDD emitter follower) | Nexperia | BC817-25,215 | SOT-23 | ORDERABLE | docs/datasheets/power-semiconductors/BC817.pdf | 0.024100 | 0.0241 | LCSC C39828 @300+ (2026-10-04) | high | 0.020900 | REAL: LCSC C39828 @3000+ break (annual qty 5000)
301 | 8 | DAB60: 8 | BSS138BK | N-MOSFET 60 V 360 mA | Nexperia | BSS138BK | SOT-23 | ORDERABLE | docs/datasheets/power-semiconductors/BSS138BK.pdf | 0.038300 | 0.3064 | LCSC C282529 @1000+ (2026-10-05) | high | 0.038300 | REAL: LCSC C282529 @1000+ break (annual qty 40000)
302 | 1 | AUX-HV_DAB: 1 | BZX84-A18,215 | Zener 18 V 1 % (VDD follower reference = SiC gate drive) | Nexperia | BZX84-A18,215 | SOT-23 | ORDERABLE | docs/datasheets/protection/BZX84.pdf | 0.582100 | 0.5821 | estimate BZX84-A18,215: ESTIMATE: LCSC lists the 1 % A-series BZX84-A18,215 from 0.5821 USD (web-search result 2026-10-04, single piece); sim/out/aux_hv_design/a... | low | 0.494785 | ASSUMED x0.85 [asia_part_estimate]
303 | 8 | DAB60: 8 | BZX84-B16 | Zener 16 V 2 % 250 mW (gate clamp, positive) | Nexperia | BZX84-B16 | SOT-23 | ORDERABLE | docs/datasheets/protection/BZX84.pdf | 0.014500 | 0.1160 | estimate BZX84-B16: ESTIMATE: no LCSC listing found for this voltage; the 2 % B-series BZX84-B12,215 is 0.0145 USD at 600+ on LCSC (C282540, 2026-10-04), sam... | medium | 0.012325 | ASSUMED x0.85 [asia_part_estimate]
304 | 1 | AUX-HV_DAB: 1 | BZX84-B20,215 | Zener 20 V 2 % (VDD / gate over-voltage clamp) | Nexperia | BZX84-B20,215 | SOT-23 | ORDERABLE | docs/datasheets/protection/BZX84.pdf | 0.019400 | 0.0194 | estimate BZX84-B20,215: ESTIMATE: no break table for this voltage in the mirror (LCSC lists it, 840 pcs, 0.0428 at qty 1); the same 2 % B-series BZX84-B18,215 is... | medium | 0.016490 | ASSUMED x0.85 [asia_part_estimate]
305 | 1 | AUX-HV_DAB: 1 | BZX84-B3V3,215 | Zener 3.3 V 2 % (PG buffer rail) | Nexperia | BZX84-B3V3,215 | SOT-23 | ORDERABLE | docs/datasheets/protection/BZX84.pdf | 0.050200 | 0.0502 | LCSC C182377 @1000+ (2026-10-05) | high | 0.050200 | REAL: the catalogue price is already the lowest published (LCSC C182377)
306 | 8 | DAB60: 8 | BZX84-B5V6 | Zener 5.6 V 2 % 250 mW (gate clamp, negative) | Nexperia | BZX84-B5V6 | SOT-23 | ORDERABLE | docs/datasheets/protection/BZX84.pdf | 0.028800 | 0.2304 | LCSC C183269 @300+ (2026-10-04) | high | 0.021700 | REAL: LCSC C183269 @9000+ break (annual qty 40000)
307 | 1 | AUX-HV_DAB: 1 | BZX84-B6V8,215 | Zener 6.8 V 2 % (foldback threshold) | Nexperia | BZX84-B6V8,215 | SOT-23 | ORDERABLE | docs/datasheets/protection/BZX84.pdf | 0.014500 | 0.0145 | estimate BZX84-B6V8,215: ESTIMATE: no LCSC listing found for this voltage; the 2 % B-series BZX84-B12,215 is 0.0145 USD at 600+ on LCSC (C282540, 2026-10-04), sam... | medium | 0.012325 | ASSUMED x0.85 [asia_part_estimate]
308 | 1 | SYS-IO-AUX: 1 | BZX84-C12,215 | Zener 12 V 5 % 250 mW | Nexperia | BZX84-C12,215 | SOT-23 | ORDERABLE | docs/datasheets/protection/BZX84.pdf | 0.016100 | 0.0161 | LCSC C108437 @600+ (2026-10-04) | high | 0.014100 | REAL: LCSC C108437 @3000+ break (annual qty 5000)
309 | 2 | DAB60: 2 | BZX84-C15 | Zener 15 V 250 mW | Nexperia | BZX84-C15 | SOT-23 | ORDERABLE | docs/datasheets/protection/BZX84.pdf | 0.045300 | 0.0906 | LCSC C143972 @500+ (2026-10-04) | high | 0.037600 | REAL: LCSC C143972 @6000+ break (annual qty 10000)
310 | 10 | BMU-GW: 2; SYS-IO-AUX: 8 | PMEG4010CEJ | Schottky rectifier 40 V 1 A low Vf | Nexperia | PMEG4010CEJ | SOD-323F | ORDERABLE | https://www.nexperia.com/product/PMEG4010CEJ | 0.302600 | 3.0260 | LCSC C50704 @1000+ (2026-10-04) | high | 0.302600 | REAL: LCSC C50704 @1000+ break (annual qty 50000)
311 | 2 | DAB60: 2 | G7L-2A-X DC24 | Precharge relay DPST-NO, poles in series: 25 A @ 1000 VDC normal polarity only, 24 V coil 250 ohm | Omron | G7L-2A-X DC24 | PCB relay 52.5x35.5 mm | ORDERABLE | docs/datasheets/protection/G7L-X.pdf | 12.710000 | 25.4200 | estimate G7L-2A-X DC24: ESTIMATE: no price for the -X variant; DigiKey G7L-2A-BUBJ-CB-IN DC24 is 12.71 USD at 260+, Mouser G7L-2A-P-PV-DC24 is 10.18 USD at 260 (... | low | 10.168000 | ASSUMED x0.80 [protection_estimate]
312 | 2 | SYS-IO-AUX: 2 | 1720466 | PCB header 2-pos 7.62 mm, 41 A 630 V (maker listing), 24 V feed | Phoenix Contact | 1720466 | PC 5/ 2-G-7.62 THT | ORDERABLE | https://www.phoenixcontact.com/en-us/products/pcb-header-pc-5-2-g-762-1720466 | 1.900000 | 3.8000 | estimate 1720466: ESTIMATE: Phoenix Contact PC 5/2-G-7.62 2-pos header, no price read; the same family 1720576 (PCV 5/2-G-7.62) is listed 1.71-2.96 USD at... | low | 1.615000 | ASSUMED x0.85 [asia_part_estimate]
313 | 1 | SYS-IO-AUX: 1 | 1720479 | PCB header 3-pos 7.62 mm, 41 A 630 V (maker listing), AUX-HV feed | Phoenix Contact | 1720479 | PC 5/ 3-G-7.62 THT | ORDERABLE | https://www.phoenixcontact.com/en-us/products/pcb-header-pc-5-3-g-762-1720479 | 2.600000 | 2.6000 | estimate 1720479: ESTIMATE: 3-pos 7.62 mm header, scaled from the 2-pos estimate (about 1.35x) | low | 2.210000 | ASSUMED x0.85 [asia_part_estimate]
314 | 1 | AUX-HV_DAB: 1 | 1720479 | PCB header 3-pos 7.62 mm (interfaces.AUX output) | Phoenix Contact | 1720479 | PC 5/ 3-G-7.62 THT | ORDERABLE | https://www.phoenixcontact.com/en-us/products/pcb-header-pc-5-3-g-762-1720479 | 2.600000 | 2.6000 | estimate 1720479: ESTIMATE: 3-pos 7.62 mm header, scaled from the 2-pos estimate (about 1.35x) | low | 2.210000 | ASSUMED x0.85 [asia_part_estimate]
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
