vectivolt/PCM/docs/reference-designs/megarevo/pma/MANUAL-NOTES.md

# Megarevo PMA series user manual — module-level statements (competitor notes)

- **Source:** `pma_user-manual_20250327-v2-00.pdf` ("PMA SERIES USER MANUAL", 45 PDF pages, 18,683,363 bytes, sha256 `5ab52833fcf519dbad693e051490d9e1e8ccf07a52f5d01d54c99e754d50ea65`; the manifest row in `docs/SOURCES.csv` carries the same hash). Origin: https://www.megarevo.com/upload/download/PMA-Standard%20Neutral-A4-20250327-EN-V2.00_A.pdf, linked from the PMA product page. The cover prints "VER: V2.10"; the site file name and our file name say V2.00 (an inconsistency inside the manual).
- **Retrieved:** 2026-10-04. **Read:** 2026-10-06 — text layer with `pdftotext -layout`, plus the page images for every figure and software screenshot (pp. 7-21 and 27-35; screenshots read at 300-450 dpi).
- **Status:** competitor's *published* statements, not measured and not verified by us. Sections 1-5 restate the manual. Sections 6-8 compare it with the datasheets and with itself and list what it does not say. Section 9 is arithmetic on the published figures and is labelled as ours. No design claim or requirement of ours appears in this note.
- **Wording:** paraphrased, not quoted. Connector labels, pin names, menu and parameter names (with the manual's own spelling) and numbers are reproduced as printed.
- **Page references:** `p.N` is the PDF page (1-45). The manual's printed page number is N − 2 for pp. 3-44. `§` is the manual's section number. *fig.* marks a statement taken from a drawing or photograph, *scr.* one taken from a software screenshot; unmarked statements are text or tables.
- **Scope:** modules only. The manual covers PMA0050, PMA0060, PMA0080B / PMA0080F and PMA0105B / PMA0105F (the cover lists six model codes). **It does not cover the 125 kW module**: the only 125 kW mention is one code in the model-name legend (p.7); the specification tables, the air-duct table, the breaker table and the cable table all stop at 105 kW. The PMA0125 / PMA0135 figures are in `spec-pma0125.md` and in the datasheet. Cabinet, rack, mechanical and touch-screen content is skipped except where it states a module interface or requirement.
- **Software screenshots:** the connected PC-tool screenshots (pp. 29-30) come from a unit whose status bar reads PMA-62.5kW, DSP version V001B001D017, protocol version V001B000D003, serial 9600-8-N-1. Parameter ranges read from them belong to that 62.5 kW unit.

---

## 1. Electrical interfaces of the module

### 1.1 What the drawing puts inside the module (Figures 3-7 and 3-8, p.10, *fig.*)

The block drawing runs from the DC terminals to the AC terminals:

| # | Block shown | Note |
|---|---|---|
| 1 | DC+ and DC- terminals, one DC fuse in each pole | |
| 2 | DC SPD (surge arrester) to PE | on the terminal side of the DC fuses |
| 3 | "Soft start" block; the label "DC contactor" sits under it | no timing or sequence is given anywhere in the manual |
| 4 | DC EMC filter | |
| 5 | "ISO" element across the two DC lines | the parameter tables list insulation-resistance detection as integrated (pp.39, 43) |
| 6 | DC link: two capacitors in series with a midpoint | |
| 7 | Three-level converter ("Three-Level PCS") | the model-name legend calls the module a DC/AC single-stage converter (p.7) |
| 8 | LCL filter, then AC EMC filter | |
| 9 | AC contactor, three poles drawn, with a "GFCI" ring around the phase lines | |
| 10 | One AC fuse in each phase, then terminals A, B, C (and N in Figure 3-8) | |
| 11 | AC SPD to PE | on the terminal side of the AC fuses |

Features text (§3.1.5, p.10): the three-level topology gives a wide charge and discharge voltage range when several units run in parallel; mid-point balancing can adjust the DC component and the low-frequency pulsating current on the "bypass bus" (as printed); SPD, ISO and GFCI monitoring are fitted and coordinated with the electrical protection; the module is a standard rack-mount design.

### 1.2 Power terminals

| Module | DC terminals | AC terminals | PE | Pages |
|---|---|---|---|---|
| PMA0050, PMA0060 | at the back; supplied terminal block type DL17Z-5 on the right side; DC+ above DC- | at the back; terminal block type DL17Z-5 on the left side; A, B, C from right to left; N is the upper position in the C column (*fig.* labels N above C) | chassis grounding point at the right-hand end of the back panel, next to the DC connector (*fig.* pp.12, 27); the text says beside the AC terminal (p.26) | pp.11-12, 24, 26-27 |
| PMA0080B, PMA0105B (back wiring) | at the back; M6 screws; DC+ then DC- from right to left | M8 screws; A, B, C, N from right to left | grounding stud next to the AC block | pp.14-15, 26-27 |
| PMA0080F, PMA0105F (front wiring) | at the front; M6 screws; DC- then DC+ from right to left | M8 screws; N, C, B, A from right to left | same | pp.15, 26-27 |

- Connector type, from the parameter tables: 50/60 kW quick connector that supports hot plug (p.40); 80/105 kW OT/DT terminal, permanently connected (p.43).
- *fig.* (pp.12, 27): the 50/60 kW power connectors are hybrid blocks with a small multi-pin block between the power contacts; the manual does not label or describe it. The 80/105 kW photographs show shrouded red (DC+) and black (DC-) lugs and a four-pole AC barrier strip (pp.9, 15).
- Ground conductor (Table 4-5, p.25): at least 16 mm² (50 kW), 25 mm² (62.5 kW), 35 mm² (80 and 105 kW).
- Where copper meets aluminium the manual asks for a dedicated copper-aluminium connector (p.26).

### 1.3 Neutral handling

| Statement | Page |
|---|---|
| Every module supports two grid types, 3W+PE and 3W+N+PE, with a separate DC window for each: 3W+PE operating 590-950 V, full load 600-900 V; 3W+N+PE operating 650-950 V, full load 680-900 V | pp.37, 38, 41 |
| The 80/105 kW AC port has four positions (A, B, C, N); on the 50/60 kW module N is the upper position in the C column | pp.9, 12, 15 |
| Single module: connect grid A, B, C and leave the N port unconnected | pp.12, 15 |
| Several modules on one common battery: join the N terminals of the modules to each other and do not connect them to the grid neutral | pp.12, 15 |
| Several modules on separate batteries: leave the module N lines unconnected from one another and from the grid neutral | pp.12, 15 |
| Figure 3-8 (3W+N+PE), *fig.*: the DC-link capacitor midpoint is wired to the N terminal, through the LCL and AC EMC filters; no contactor or fuse symbol is drawn in that line; the GFCI ring is drawn around the three phase lines and its lower tip touches the N line, so the drawing does not settle whether N passes through the ring. Figure 3-7 (3W+PE): the midpoint goes only to the converter's own neutral-point input | p.10 |
| Cable table: no N cable for a single module; for paralleled modules the N cable has the cross-section of one phase conductor (35 / 50 / 70 / 70 mm² for 50 / 62.5 / 80 / 105 kW) | p.25 |
| Off-grid ratings: L-N 220 / 230 / 240 V, L-L 380 / 400 / 415 V, 100 % three-phase unbalanced load | pp.38-39, 42 |

In every wiring case the manual describes, N is not tied to the grid neutral. The manual does not describe how N is connected to the load neutral in off-grid operation, and does not say whether the N conductor passes through the residual-current ring.
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
