vectivolt/PCM/sim/out/dab_control/cv_load_step.png

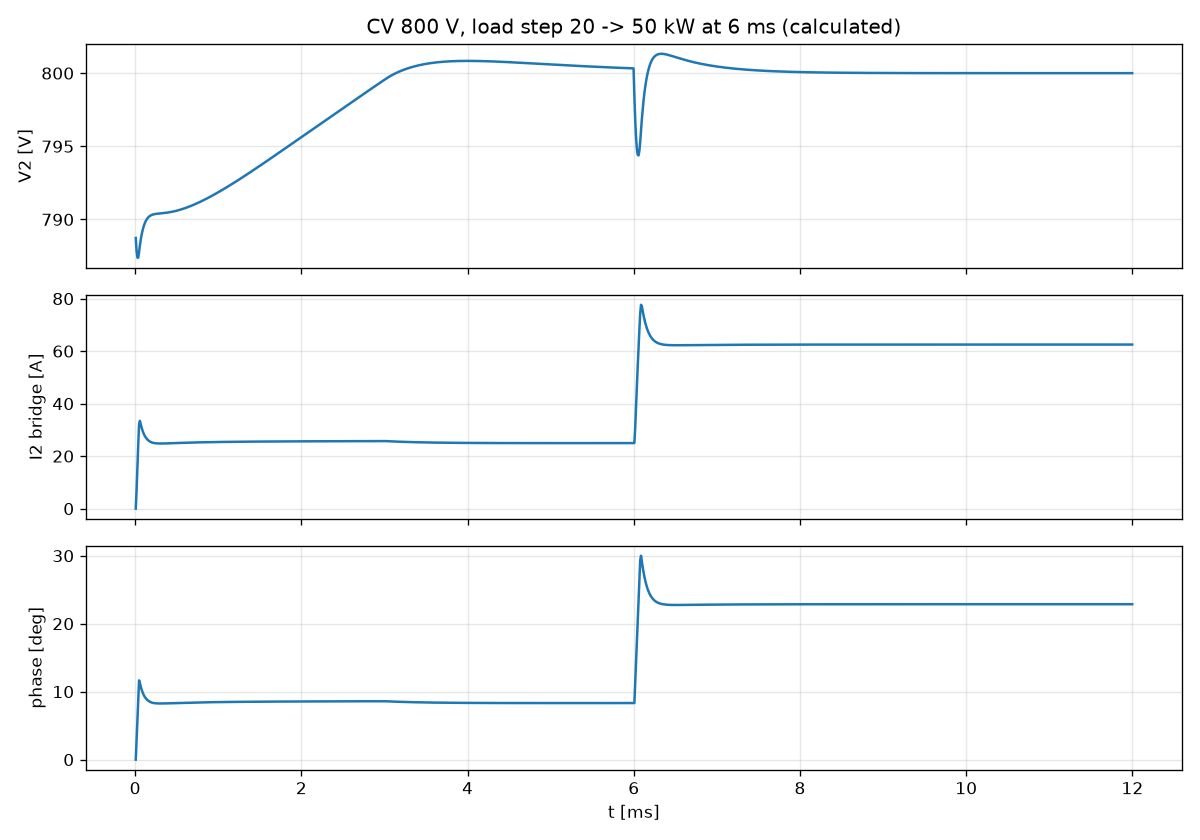
sim/out/dab_control/cv_load_step.png
