vectivolt/PCM/sim/out/pcs_control/steps.png

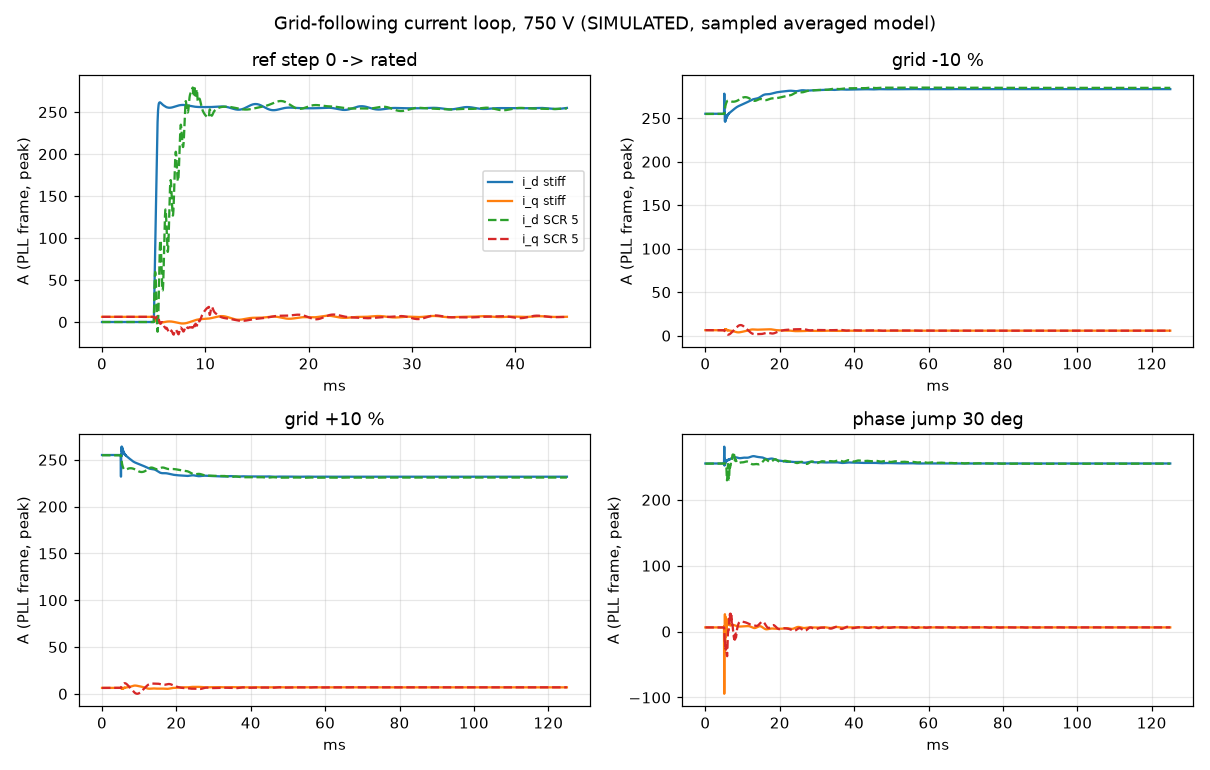
sim/out/pcs_control/steps.png
