vectivolt/PCM/hardware/PCS-PWR/outputs/PCS-PWR_schematic.pdf

1 | 2 | 3 | 4 | 5 | 6 | 7 | 8

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
Title: PCS-P125 power - Cover / Hierarchy | As AUX-HV rev C1 sheet 02: 3 x BSS126 cascode, TPS3710 brown-in 206-215 V, TLV3202 OV lockout 1107-1162 V and overload timer 39-100 ms
Size: A3 | | Rev: A0 | F Date: 2026-10-06
KiCad | E.D.A. 10.0.6 | Id: 1/28

## File: PCS-PWR.kicad_sch

## Sheet: /

## Live board referenced to DC-; gate islands functional; HV-PE basic

## Schematics authored by Chinmoy Bhuyan

## Sheet 1

Not bench-validated. Values read from sim/out/pcs_design/pcs_spec.json; checks: design_check()

# 13 Phase b LCL filter, current sensor

File: sheets/13_filtb.kicad_sch | 19 DC terminals, insulation test File: sheets/19_dcterm.kicad_sch 23 AUX75 input taps, OR, film

File: sheets/23_aux75_input.kicad_sch

# 15 AC voltage sensing

File: sheets/15_acsense.kicad_sch

# 04 Phase leg b, power stage

File: sheets/04_legb.kicad_sch

# 08 Leg b high-side gate drive

File: sheets/08_gdbh.kicad_sch

# 12 Phase a LCL filter, current sensor

# File: sheets/12_filta.kicad_sch 07 Leg a low-side gate drive

File: sheets/07_gdal.kicad_sch

# 03 Phase leg a, power stage

File: sheets/03_lega.kicad_sch

# 11 Leg c low-side gate drive

File: sheets/11_gdcl.kicad_sch

# 20 AC port: contactors, SPD, RCM

File: sheets/20_acport.kicad_sch

# 16 Port B power path (battery)

File: sheets/16_leanB_power.kicad_sch

# 24 AUX75 start-up, brown-in, OV, timer

File: sheets/24_aux75_startup.kicad_sch

# 18 Port B coil drives

File: sheets/18_leanB_drive.kicad_sch | 27 AC start-up: grid tap, AC precharge

# 01 Control connectors, defaults

File: sheets/01_pc.kicad_sch

# 05 Phase leg c, power stage

File: sheets/05_legc.kicad_sch

# 22 Live 5 V / 3.3 V, SELV connector

File: sheets/22_supplies.kicad_sch

# 14 Phase c LCL filter, current sensor

# File: sheets/14_filtc.kicad_sch 09 Leg b low-side gate drive

File: sheets/09_gdbl.kicad_sch

# 06 Leg a high-side gate drive

File: sheets/06_gdah.kicad_sch

# 10 Leg c high-side gate drive

File: sheets/10_gdch.kicad_sch

# 02 DC link, bleeders, sensing

File: sheets/02_dclink.kicad_sch

# 17 Port B sensing and interlocks

# File: sheets/17_leanB_ctrl.kicad_sch 21 PE bonds, heatsink, NTC inputs

File: sheets/21_pe.kicad_sch | +24V (aux live) -> +5V and +5V_GD (LMR38020), +3V3 (TPS62130 from +5V_GD, ramp-up and discharge), +5V_GD supervisor, SELV connector to the control board | Grid tap (K2O_x): 20 ohm, 1.6 A / 500 V AC fuse, 6 x BYG10Y; OR diode into the aux

input; AC precharge G7L-2A-X + 220 ohm from the tap's + rail to DC+ (K_ACPRE) DC terminals 250 A, X / Y capacitors, board entries, removable PE link,

port status to PCS_PC, insulation monitor (port.lean_imd) | L2 out -> K1 -> K2 -> CM choke -> AC terminals; coil drivers (fail-safe high | side); 3 x TVT25751 + 3 x Y1 to PE_T; type-B RCM sensor Switch node -> L1 (chassis) -> sensor -> C_f node F_C: C_f 2 x 25 uF + R_d-C_d
to the star M (DC midpoint) -> L2 (chassis) -> AC port

Contactor + precharge relay: interlock logic, fail-safe high side, economiser; passive bank bleeder

PCS_PC (= PC pin for pin, 2x32) and PCS_X (2x8) to PV-CTL (PCS assembly); command pull-downs, RDY pull-up, DC- star points

# PCS-P125 power

2 x 6 x SG2M040170HJ on Al2O3 pads (earthed section c); 10 k + 1 nF per gate; 3 sub-cells: 3 x 2.2 uF film + RC damper each

gdrv.channel() 6 x SG2M040170HJ: NSI6651ASC-Q1 +18/-3.5 V, 8.75/8.75 ohm | per device; PNP turn-off buffers, Miller clamps, booster, DESAT; bias SN6505B + T_BIAS4
Stages 1-7 drawn (gen/pcs_power.py header); OPEN items listed there and in the | design check.

References, BUS- shunt amplifier + hold-off / OC windows, dividers, dV amplifier, polarity and dV interlocks Switch node -> L1 (chassis) -> sensor -> C_f node F_B: C_f 2 x 25 uF + R_d-C_d
to the star M (DC midpoint) -> L2 (chassis) -> AC port Board PE bond, heatsink sections (earthed), heatsink NTC lug probes, L1 winding NTC leads, NTC filters (biased on the control board) UCC28C59-Q1 64.9 kHz, IV2Q171R0D7Z, Lp 0.485 mH, Np:Nlive:Nselv 50:9:10; live 24 V regulated by the FB divider (no opto); VDD from the live 24 V

2 x 6 x SG2M040170HJ on Al2O3 pads (earthed section a); 10 k + 1 nF per gate; 3 sub-cells: 3 x 2.2 uF film + RC damper each

gdrv.channel() 6 x SG2M040170HJ: NSI6651ASC-Q1 +18/-3.5 V, 8.75/8.75 ohm per device; PNP turn-off buffers, Miller clamps, booster, DESAT; bias SN6505B + T_BIAS4 gdrv.channel() 6 x SG2M040170HJ: NSI6651ASC-Q1 +18/-3.5 V, 8.75/8.75 ohm per device; PNP turn-off buffers, Miller clamps, booster, DESAT; bias SN6505B + T_BIAS4

Rev A0 | 2026-10-06 | Schematics authored by Chinmoy Bhuyan | PCS-P125: two-level SiC bridge (6 x SG2M040170HJ per switch), split DC link, LCL, ports

5 + 5 x C3D1U147 in two series halves, midpoint M (to the C_f star); bleeder per half; VB = V(DC+), VA = V(M) around VMID (REF3030E)

gdrv.channel() 6 x SG2M040170HJ: NSI6651ASC-Q1 +18/-3.5 V, 8.75/8.75 ohm per device; PNP turn-off buffers, Miller clamps, booster, DESAT gdrv.channel() 6 x SG2M040170HJ: NSI6651ASC-Q1 +18/-3.5 V, 8.75/8.75 ohm per device; PNP turn-off buffers, Miller clamps, booster, DESAT

2 x 6 x SG2M040170HJ on Al2O3 pads (earthed section b); 10 k + 1 nF per gate; 3 sub-cells: 3 x 2.2 uF film + RC damper each

Varistor Y + monitor, aR fuses Switch node -> L1 (chassis) -> sensor -> C_f node F_A: C_f 2 x 25 uF + R_d-C_d to the star M (DC midpoint) -> L2 (chassis) -> AC port

gdrv.channel() 6 x SG2M040170HJ: NSI6651ASC-Q1 +18/-3.5 V, 8.75/8.75 ohm per device; PNP turn-off buffers, Miller clamps, booster, DESAT Domains: LIVE (DC- = GND = AGND, the AC side included), GD_<leg><H/L> gate | islands (functional: NSI6651, T_BIAS4), PE (pads, heatsink, NTC lugs, Y / | varistor | / IMD crossings), SELV (AUX-T1).
CALCULATED, not measured: design_check() asserts every number on each | build (outputs/PCS-PWR_design_check.txt); values are read from sim/out/pcs_design/pcs_spec.json at build time. One tap per port (+ pole, terminal side), return = DC-: 2 x 20R R pulse-rated ahead of the 1 A / 1000 VDC fuse, BYG10Y OR; 2 x 3.3 uF / 1300 V film = surge absorber (AUX-HV rev C1 input block)

6 x (6 x 1 M ARHV06 + 4.99 k to VMID, 4.7 nF): VC1-3 at the C_f nodes, VG1-3 at the AC terminal taps; OPA2388 followers to PCS_X

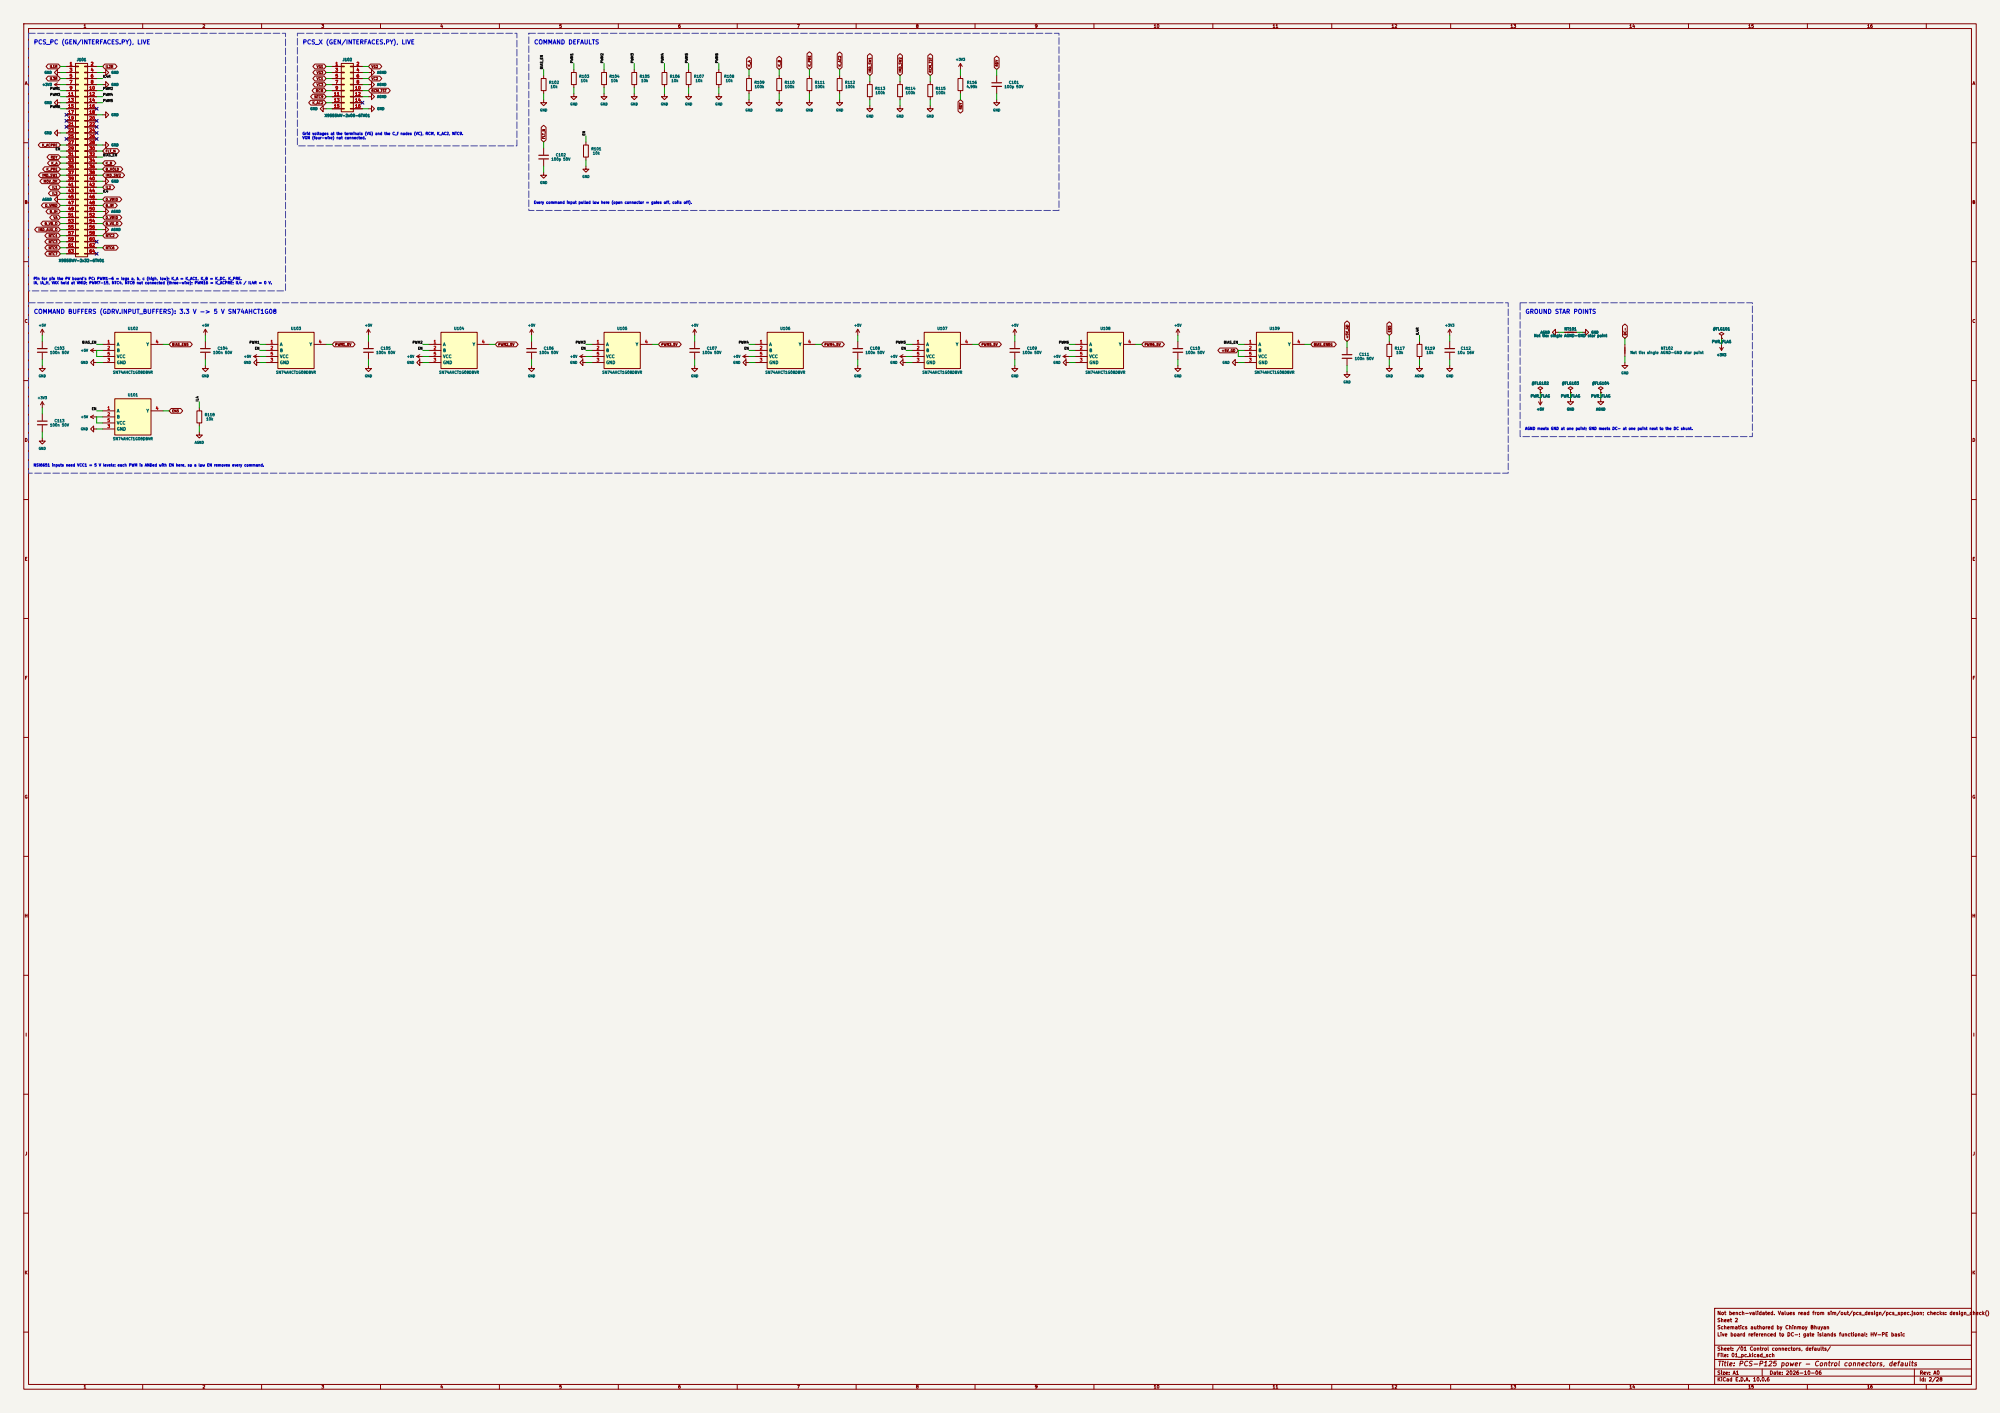
[picture p127: page 2]

PCS_PC (GEN/INTERFACES.PY), LIVE

Grid voltages at the terminals (VG) and the C_f nodes (VC), RCM, K_AC2, NTC9. VGN (four-wire) not connected.

Every command input pulled low here (open connector = gates off, coils off).

AGND meets GND at one point; GND meets DC- at one point next to the DC shunt. Pin for pin the PV board's PC: PWM1-6 = legs a, b, c (high, low); K_A = K_AC1, K_B = K_DC, K_PRE.
IA, IA_H, VAX held at VMID; PWM7-15, NTC4, NTC8 not connected (three-wire); PWM16 = K_ACPRE; IL4 / IL4R = 0 V. NSI6651 inputs need VCC1 = 5 V levels; each PWM is ANDed with EN here, so a low EN removes every command.

Not bench-validated. Values read from sim/out/pcs_design/pcs_spec.json; checks: design_check()
Sheet 2
Schematics authored by Chinmoy Bhuyan
Live board referenced to DC-; gate islands functional; HV-PE basic

Sheet: /01 Control connectors, defaults/
File: 01_pc.kicad_sch
Title: PCS-P125 power - Control connectors, defaults

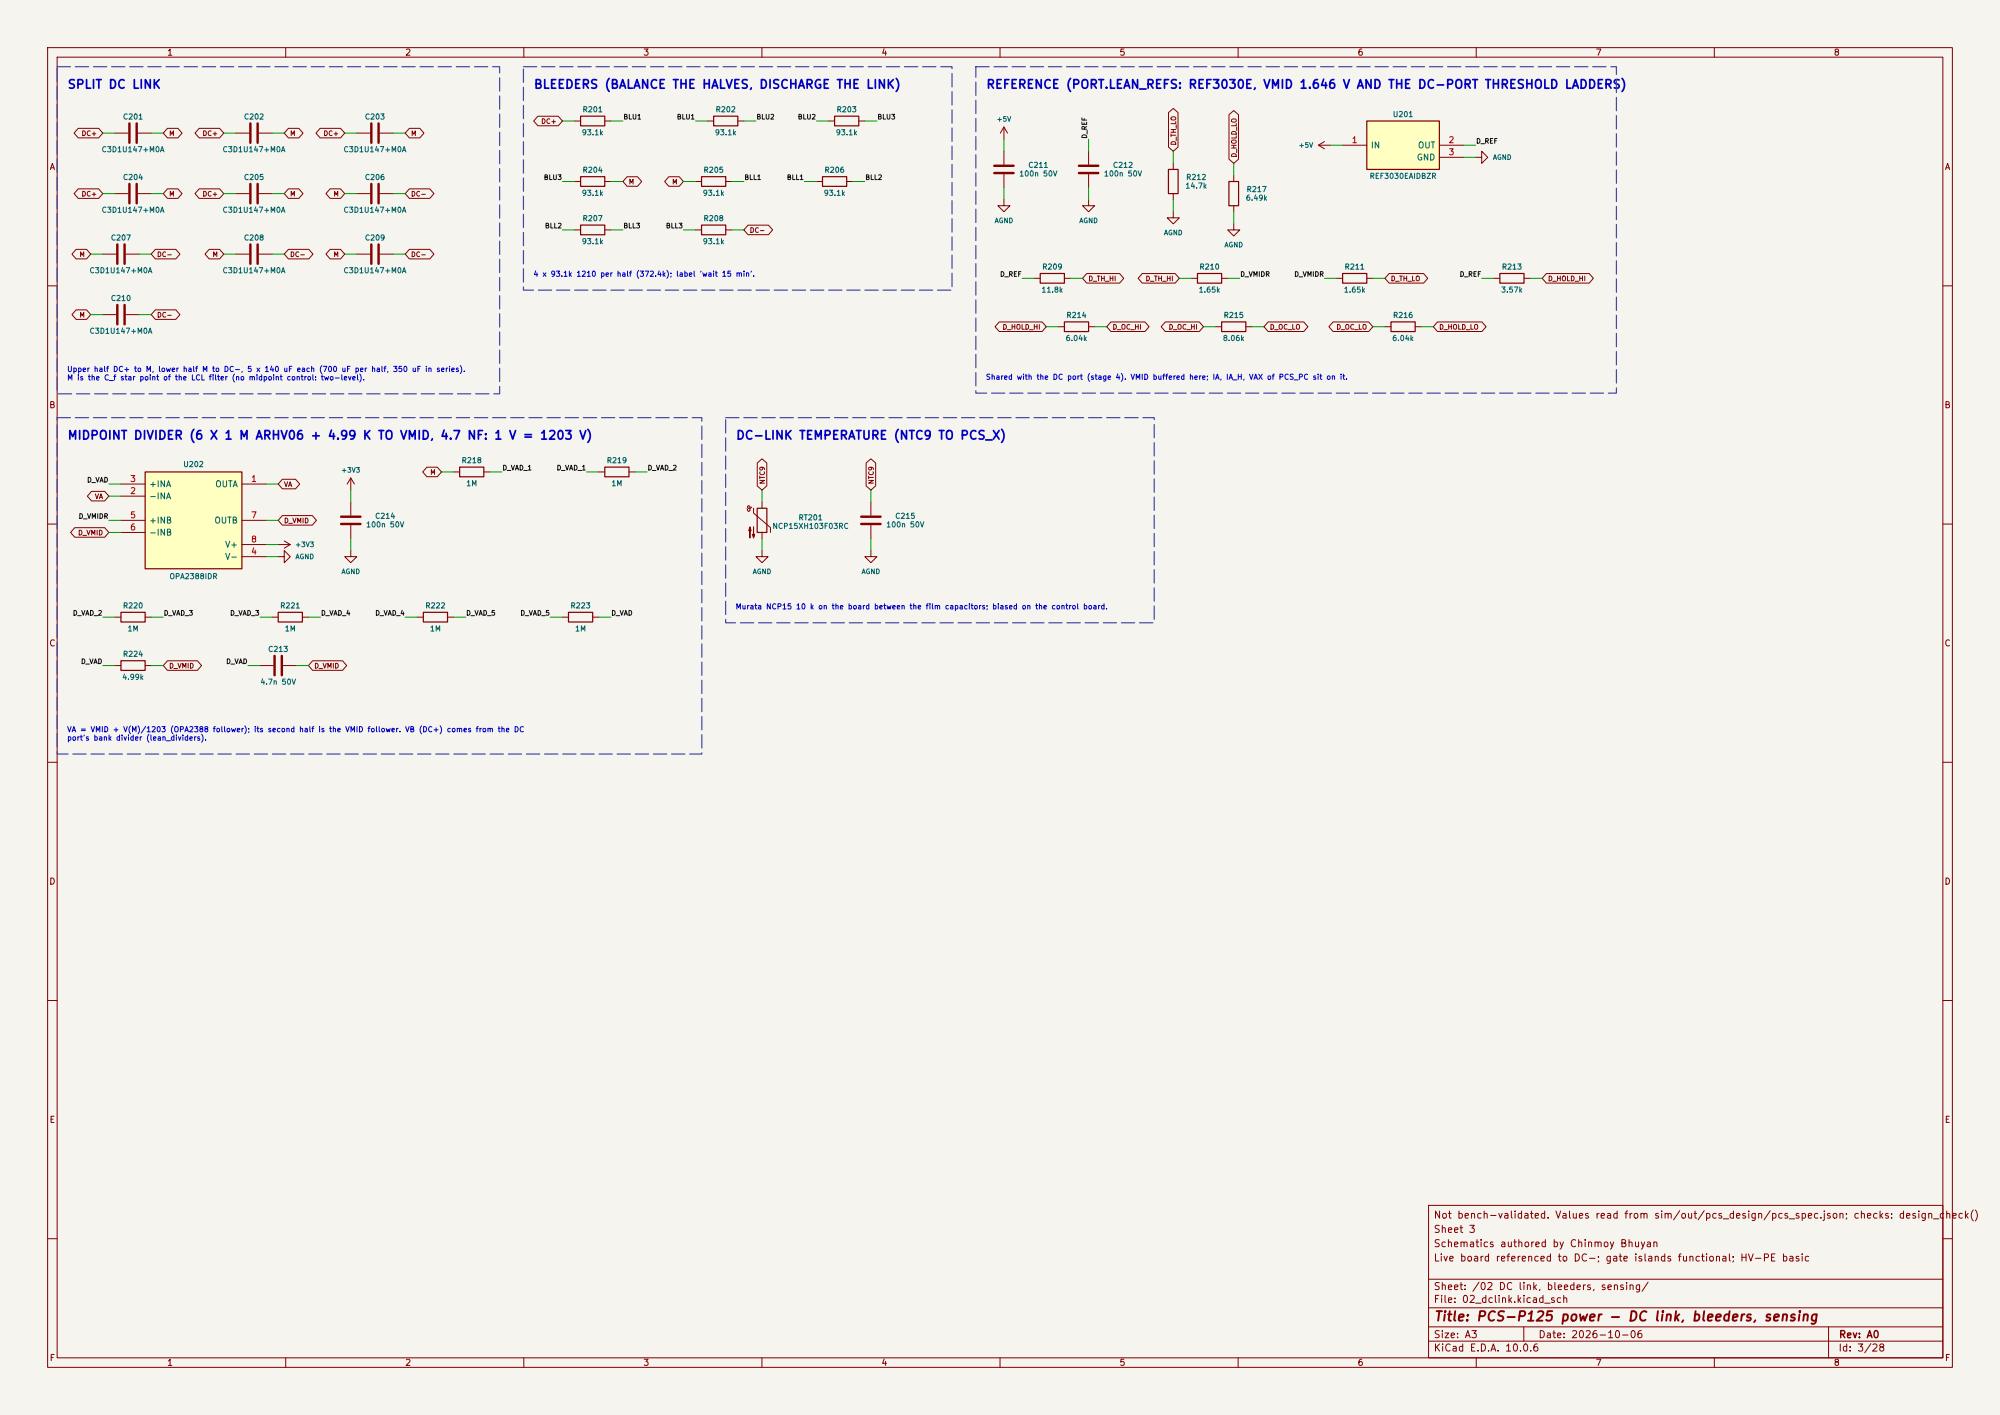
[picture p128: page 3]

SPLIT DC LINK
D_REF D_REF VA = VMID + V(M)/1203 (OPA2388 follower); its second half is the VMID follower. VB (DC+) comes from the DC

DC-LINK TEMPERATURE (NTC9 TO PCS_X) Murata NCP15 10 k on the board between the film capacitors; biased on the control board. Shared with the DC port (stage 4). VMID buffered here; IA, IA_H, VAX of PCS_PC sit on it. MIDPOINT DIVIDER (6 X 1 M ARHV06 + 4.99 K TO VMID, 4.7 NF: 1 V = 1203 V)
U202 OPA2388IDR

Not bench-validated. Values read from sim/out/pcs_design/pcs_spec.json; checks: design_check()
Sheet 3
Schematics authored by Chinmoy Bhuyan
Live board referenced to DC-; gate islands functional; HV-PE basic

Sheet: /02 DC link, bleeders, sensing/
File: 02_dclink.kicad_sch
Title: PCS-P125 power - DC link, bleeders, sensing

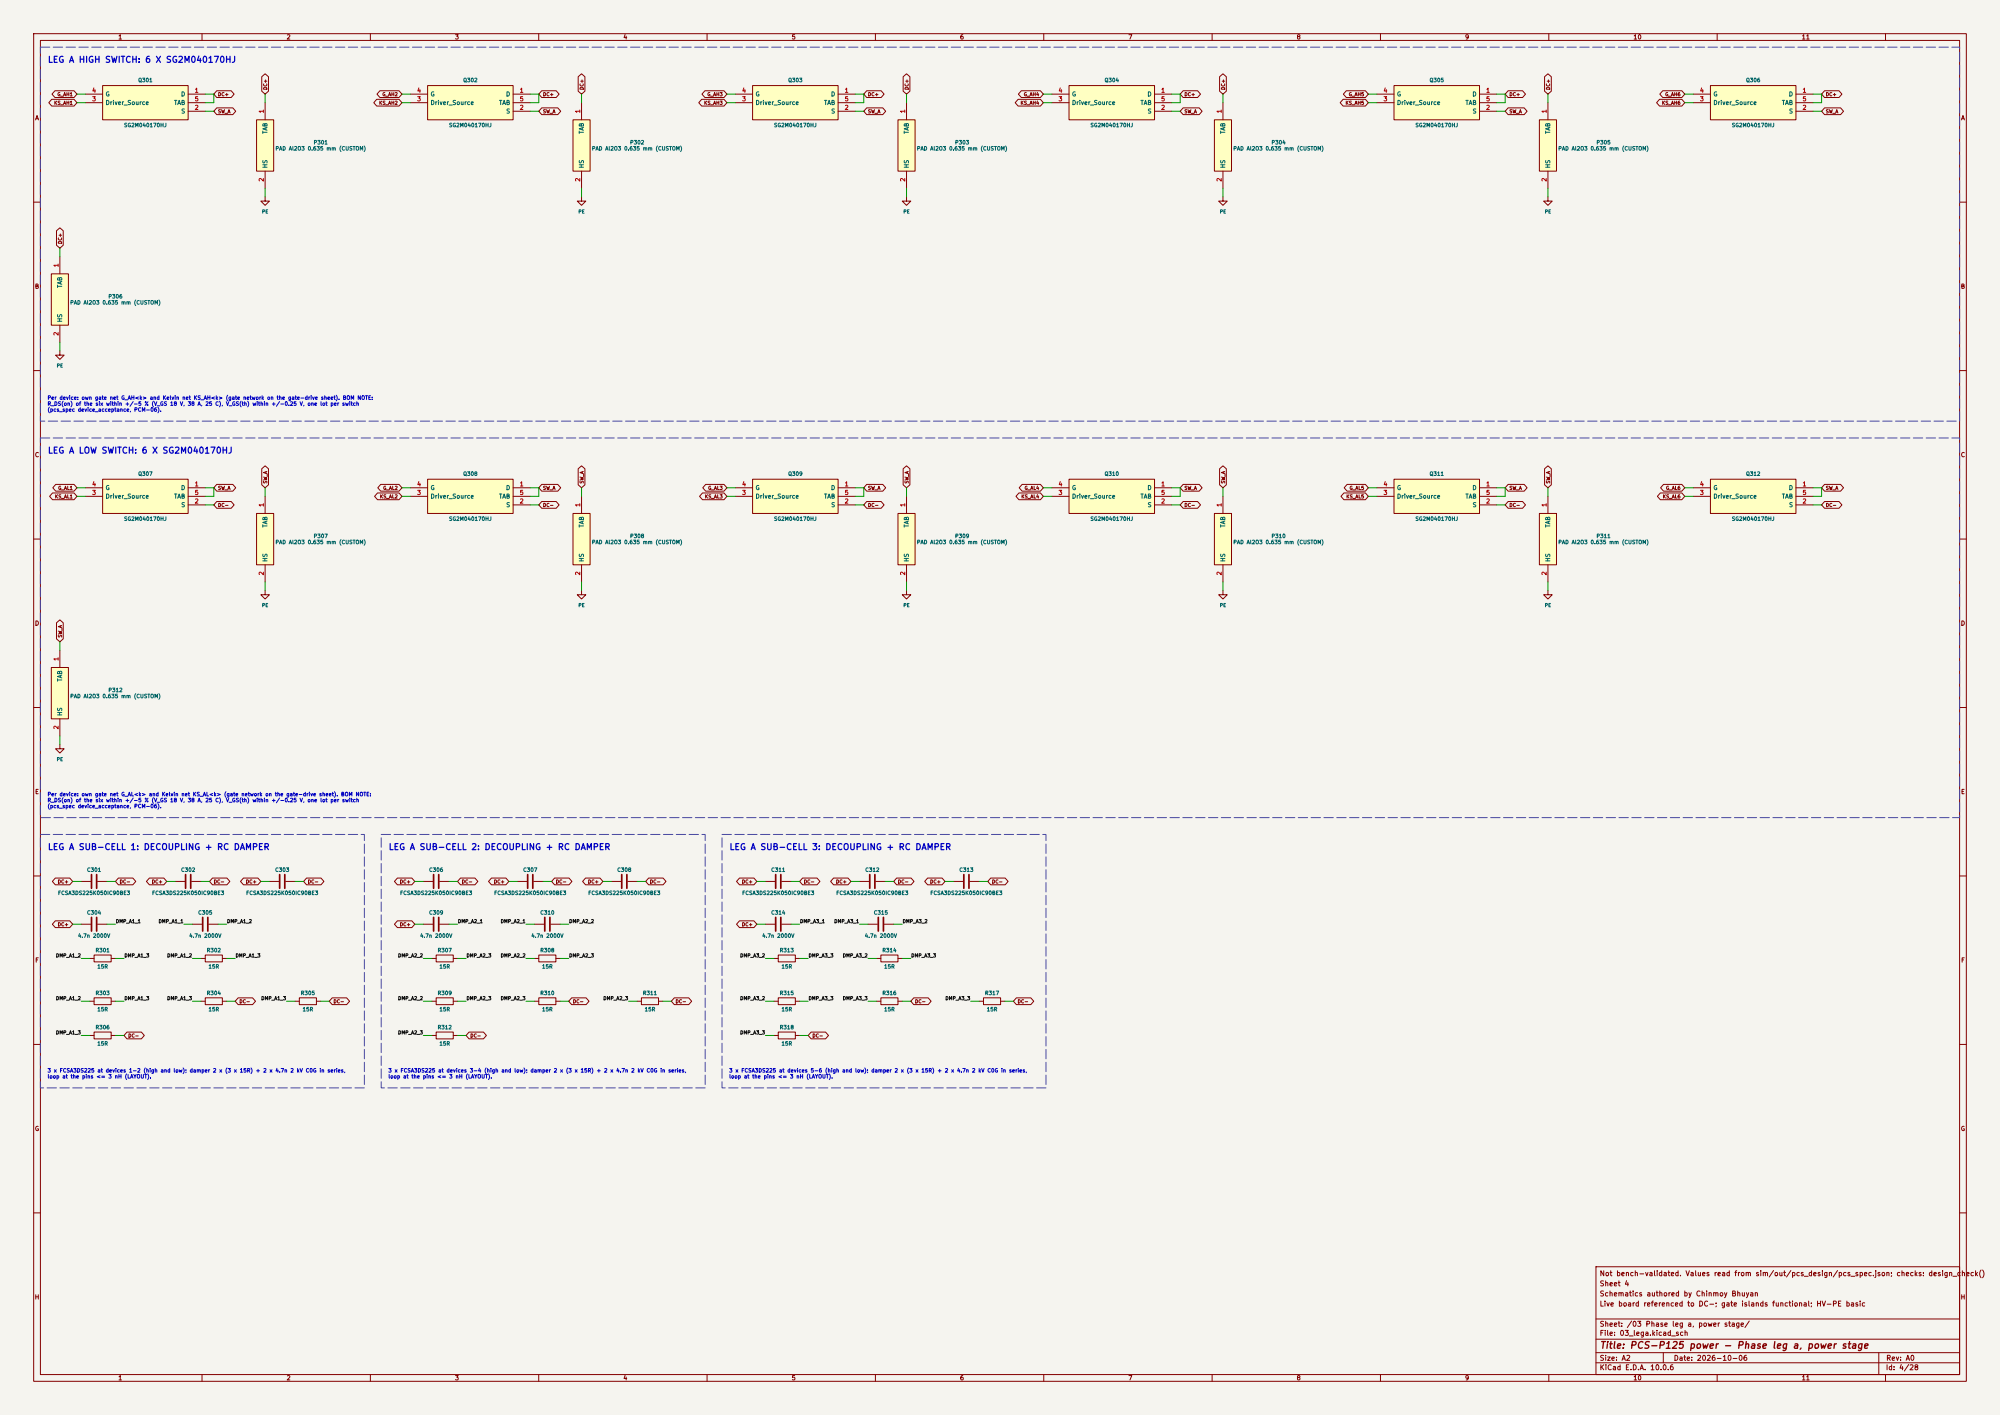
[picture p129: page 4]

P305 PAD Al2O3 0.635 mm (CUSTOM) TAB

P307 PAD Al2O3 0.635 mm (CUSTOM) PE

Per device: own gate net G_AH<k> and Kelvin net KS_AH<k> (gate network on the gate-drive sheet). BOM NOTE: R_DS(on) of the six within +/-5 % (V_GS 18 V, 38 A, 25 C), V_GS(th) within +/-0.25 V, one lot per switch

P310 PAD Al2O3 0.635 mm (CUSTOM) TAB

Per device: own gate net G_AL<k> and Kelvin net KS_AL<k> (gate network on the gate-drive sheet). BOM NOTE: R_DS(on) of the six within +/-5 % (V_GS 18 V, 38 A, 25 C), V_GS(th) within +/-0.25 V, one lot per switch

LEG A SUB-CELL 1: DECOUPLING + RC DAMPER

Not bench-validated. Values read from sim/out/pcs_design/pcs_spec.json; checks: design_check()
Sheet 4
Schematics authored by Chinmoy Bhuyan
Live board referenced to DC-; gate islands functional; HV-PE basic

Sheet: /03 Phase leg a, power stage/
File: 03_lega.kicad_sch
Title: PCS-P125 power - Phase leg a, power stage

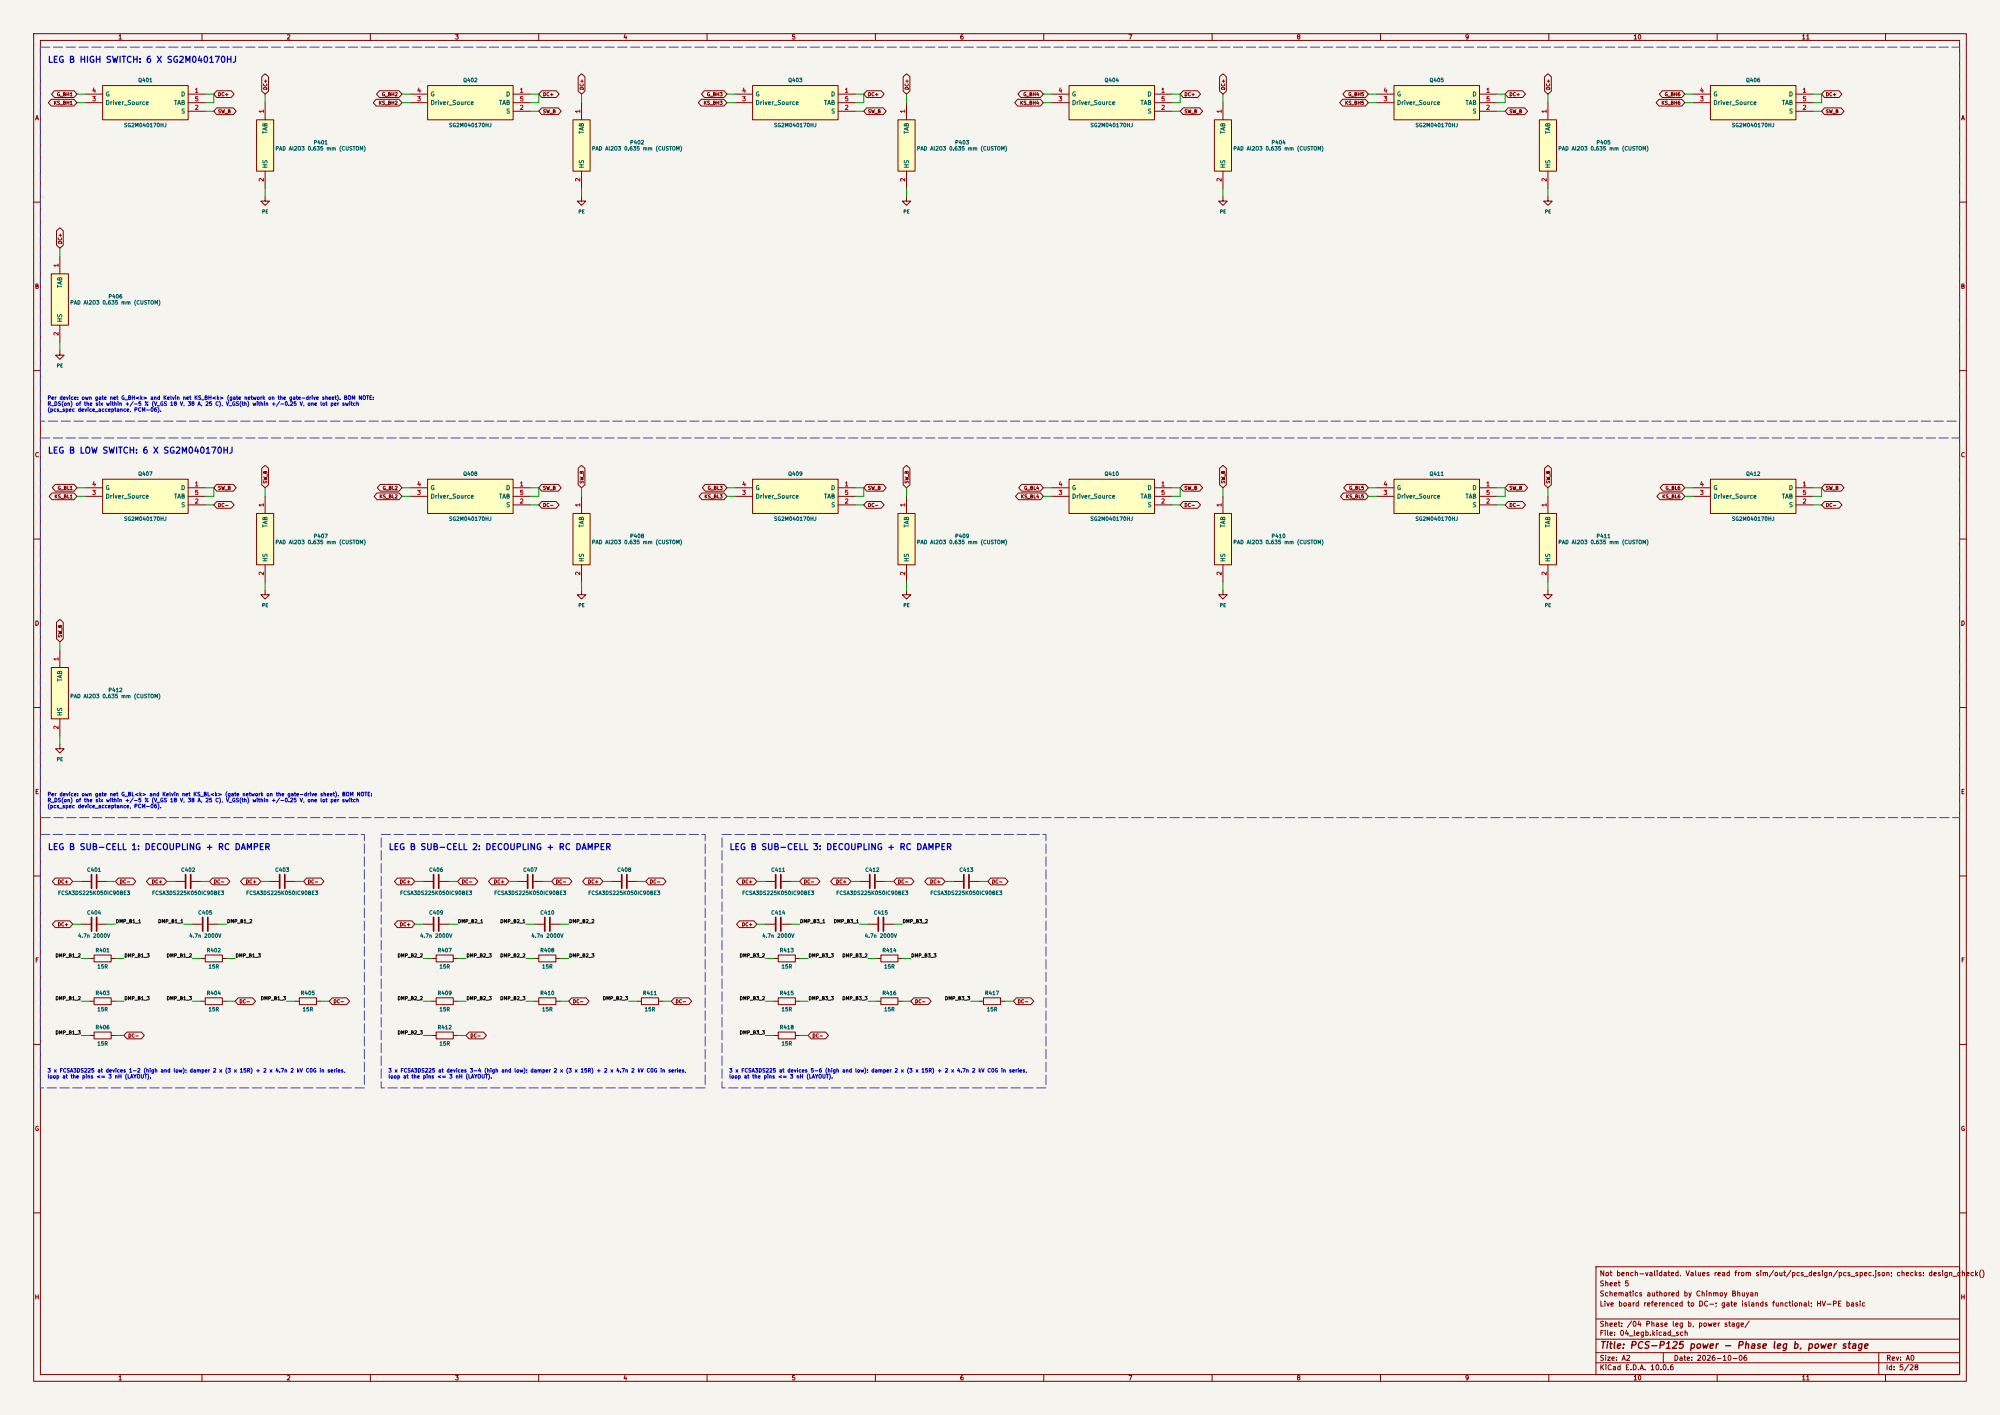
[picture p130: page 5]

P410 PAD Al2O3 0.635 mm (CUSTOM) TAB

P403 PAD Al2O3 0.635 mm (CUSTOM) PE

P406 PAD Al2O3 0.635 mm (CUSTOM) PE

Per device: own gate net G_BH<k> and Kelvin net KS_BH<k> (gate network on the gate-drive sheet). BOM NOTE: R_DS(on) of the six within +/-5 % (V_GS 18 V, 38 A, 25 C), V_GS(th) within +/-0.25 V, one lot per switch

(pcs_spec device_acceptance, PCM-06). Per device: own gate net G_BL<k> and Kelvin net KS_BL<k> (gate network on the gate-drive sheet). BOM NOTE: R_DS(on) of the six within +/-5 % (V_GS 18 V, 38 A, 25 C), V_GS(th) within +/-0.25 V, one lot per switch

LEG B SUB-CELL 1: DECOUPLING + RC DAMPER

LEG B SUB-CELL 2: DECOUPLING + RC DAMPER

LEG B SUB-CELL 3: DECOUPLING + RC DAMPER

3 x FCSA3DS225 at devices 1-2 (high and low); damper 2 x (3 x 15R) + 2 x 4.7n 2 kV C0G in series, loop at the pins <= 3 nH (LAYOUT).

3 x FCSA3DS225 at devices 3-4 (high and low); damper 2 x (3 x 15R) + 2 x 4.7n 2 kV C0G in series, loop at the pins <= 3 nH (LAYOUT).

3 x FCSA3DS225 at devices 5-6 (high and low); damper 2 x (3 x 15R) + 2 x 4.7n 2 kV C0G in series, loop at the pins <= 3 nH (LAYOUT).

Not bench-validated. Values read from sim/out/pcs_design/pcs_spec.json; checks: design_check()
Sheet 5
Schematics authored by Chinmoy Bhuyan
Live board referenced to DC-; gate islands functional; HV-PE basic

Sheet: /04 Phase leg b, power stage/
File: 04_legb.kicad_sch
Title: PCS-P125 power - Phase leg b, power stage

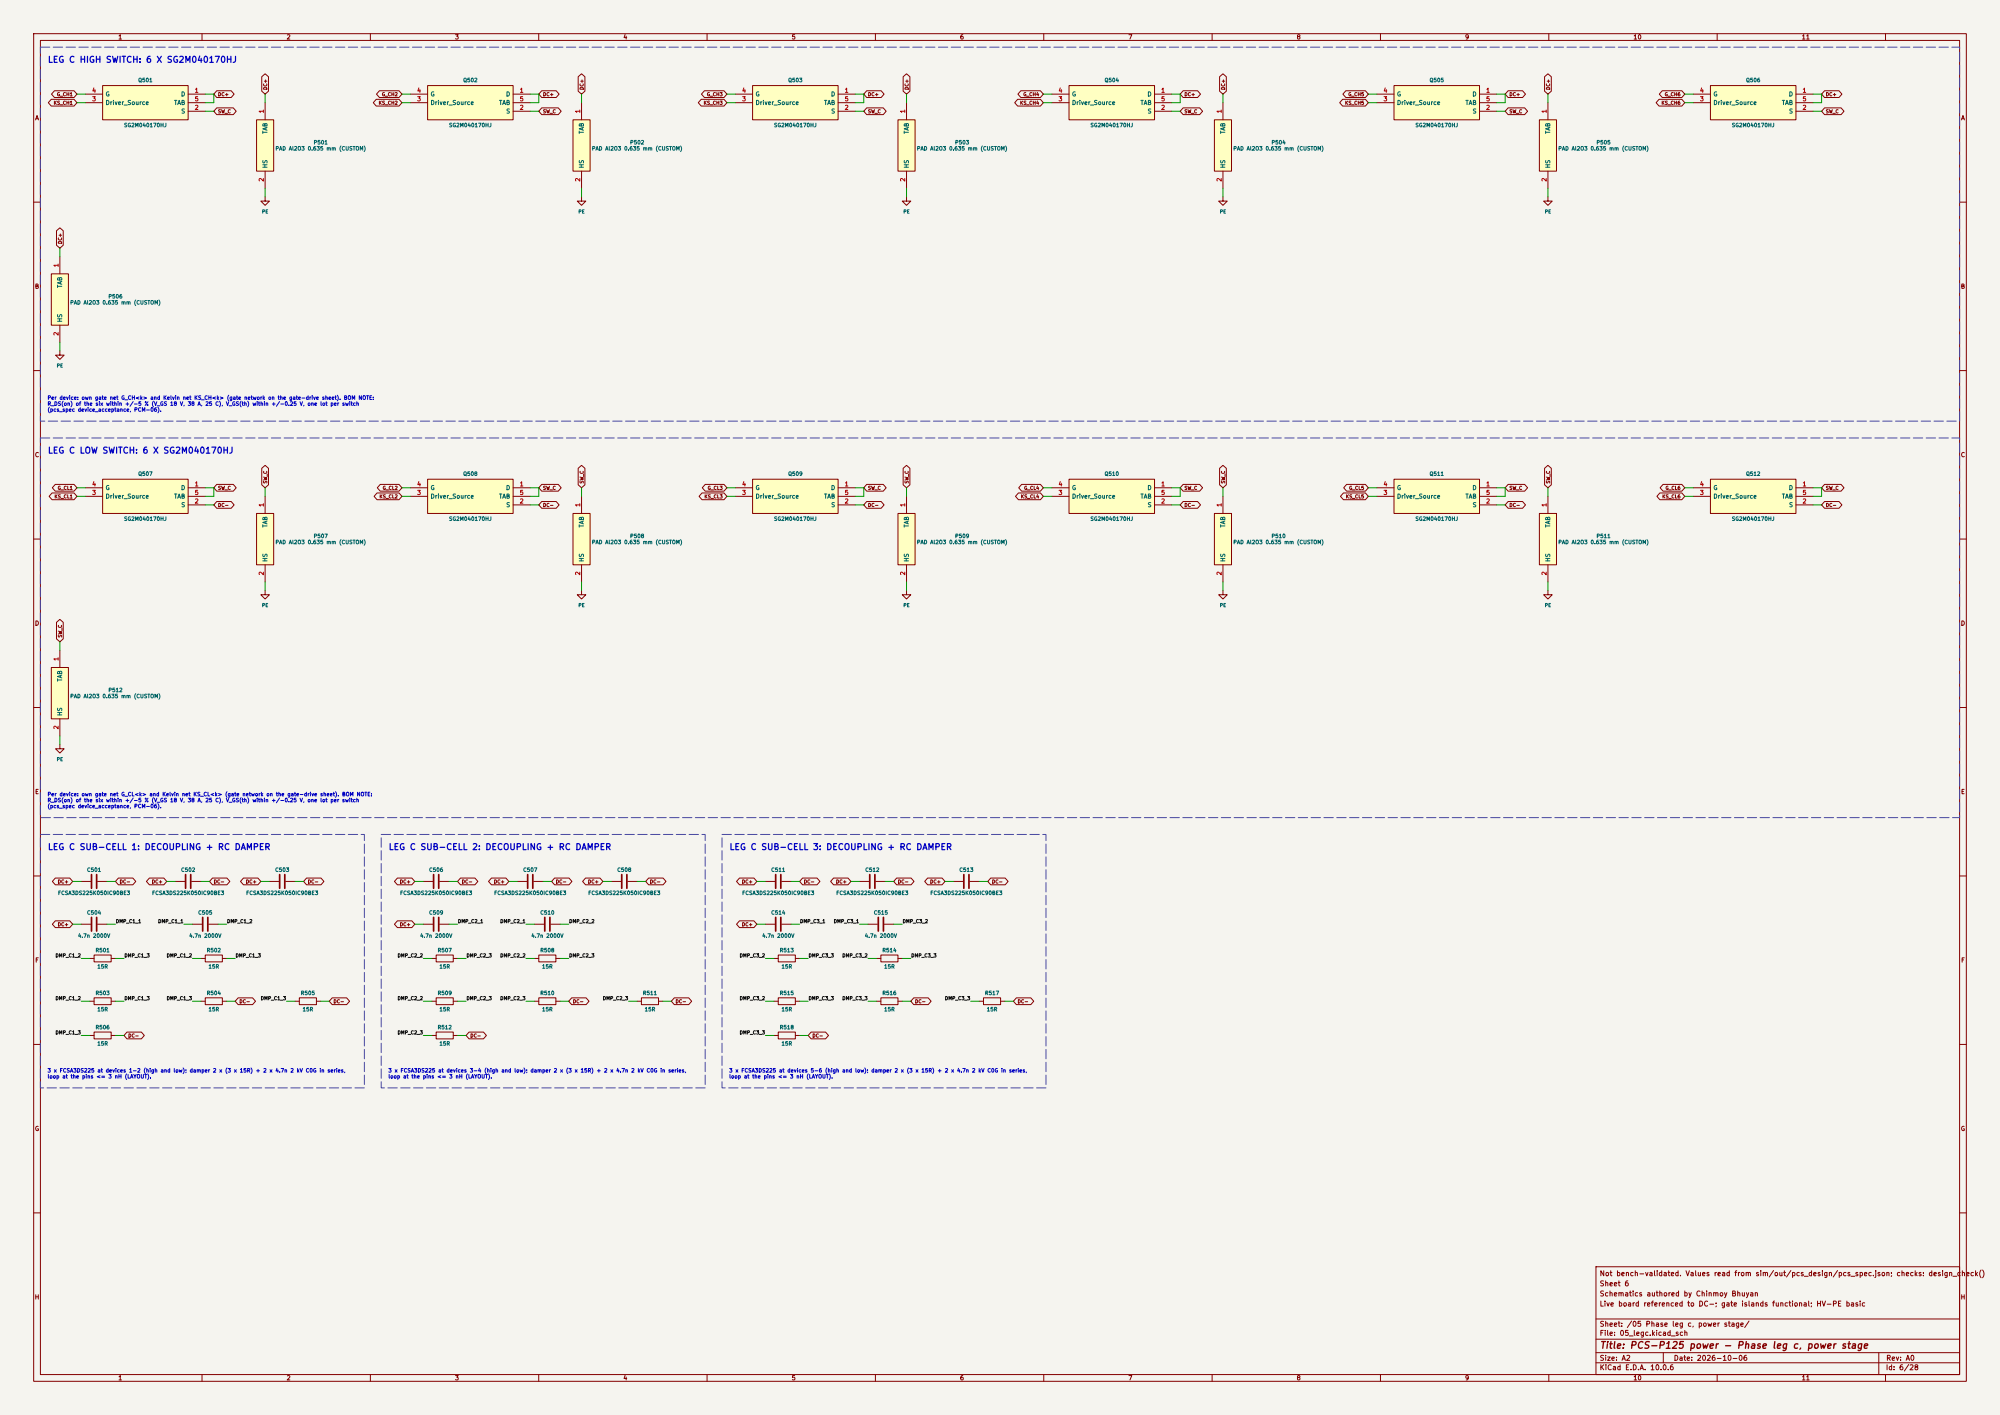
[picture p131: page 6]

Not bench-validated. Values read from sim/out/pcs_design/pcs_spec.json; checks: design_check() TAB

Per device: own gate net G_CH<k> and Kelvin net KS_CH<k> (gate network on the gate-drive sheet). BOM NOTE: R_DS(on) of the six within +/-5 % (V_GS 18 V, 38 A, 25 C), V_GS(th) within +/-0.25 V, one lot per switch

(pcs_spec device_acceptance, PCM-06). Per device: own gate net G_CL<k> and Kelvin net KS_CL<k> (gate network on the gate-drive sheet). BOM NOTE: R_DS(on) of the six within +/-5 % (V_GS 18 V, 38 A, 25 C), V_GS(th) within +/-0.25 V, one lot per switch

P511 PAD Al2O3 0.635 mm (CUSTOM) PE D

LEG C SUB-CELL 1: DECOUPLING + RC DAMPER

LEG C SUB-CELL 2: DECOUPLING + RC DAMPER

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

Sheet 6
Schematics authored by Chinmoy Bhuyan
Live board referenced to DC-; gate islands functional; HV-PE basic

Sheet: /05 Phase leg c, power stage/
File: 05_legc.kicad_sch
Title: PCS-P125 power - Phase leg c, power stage

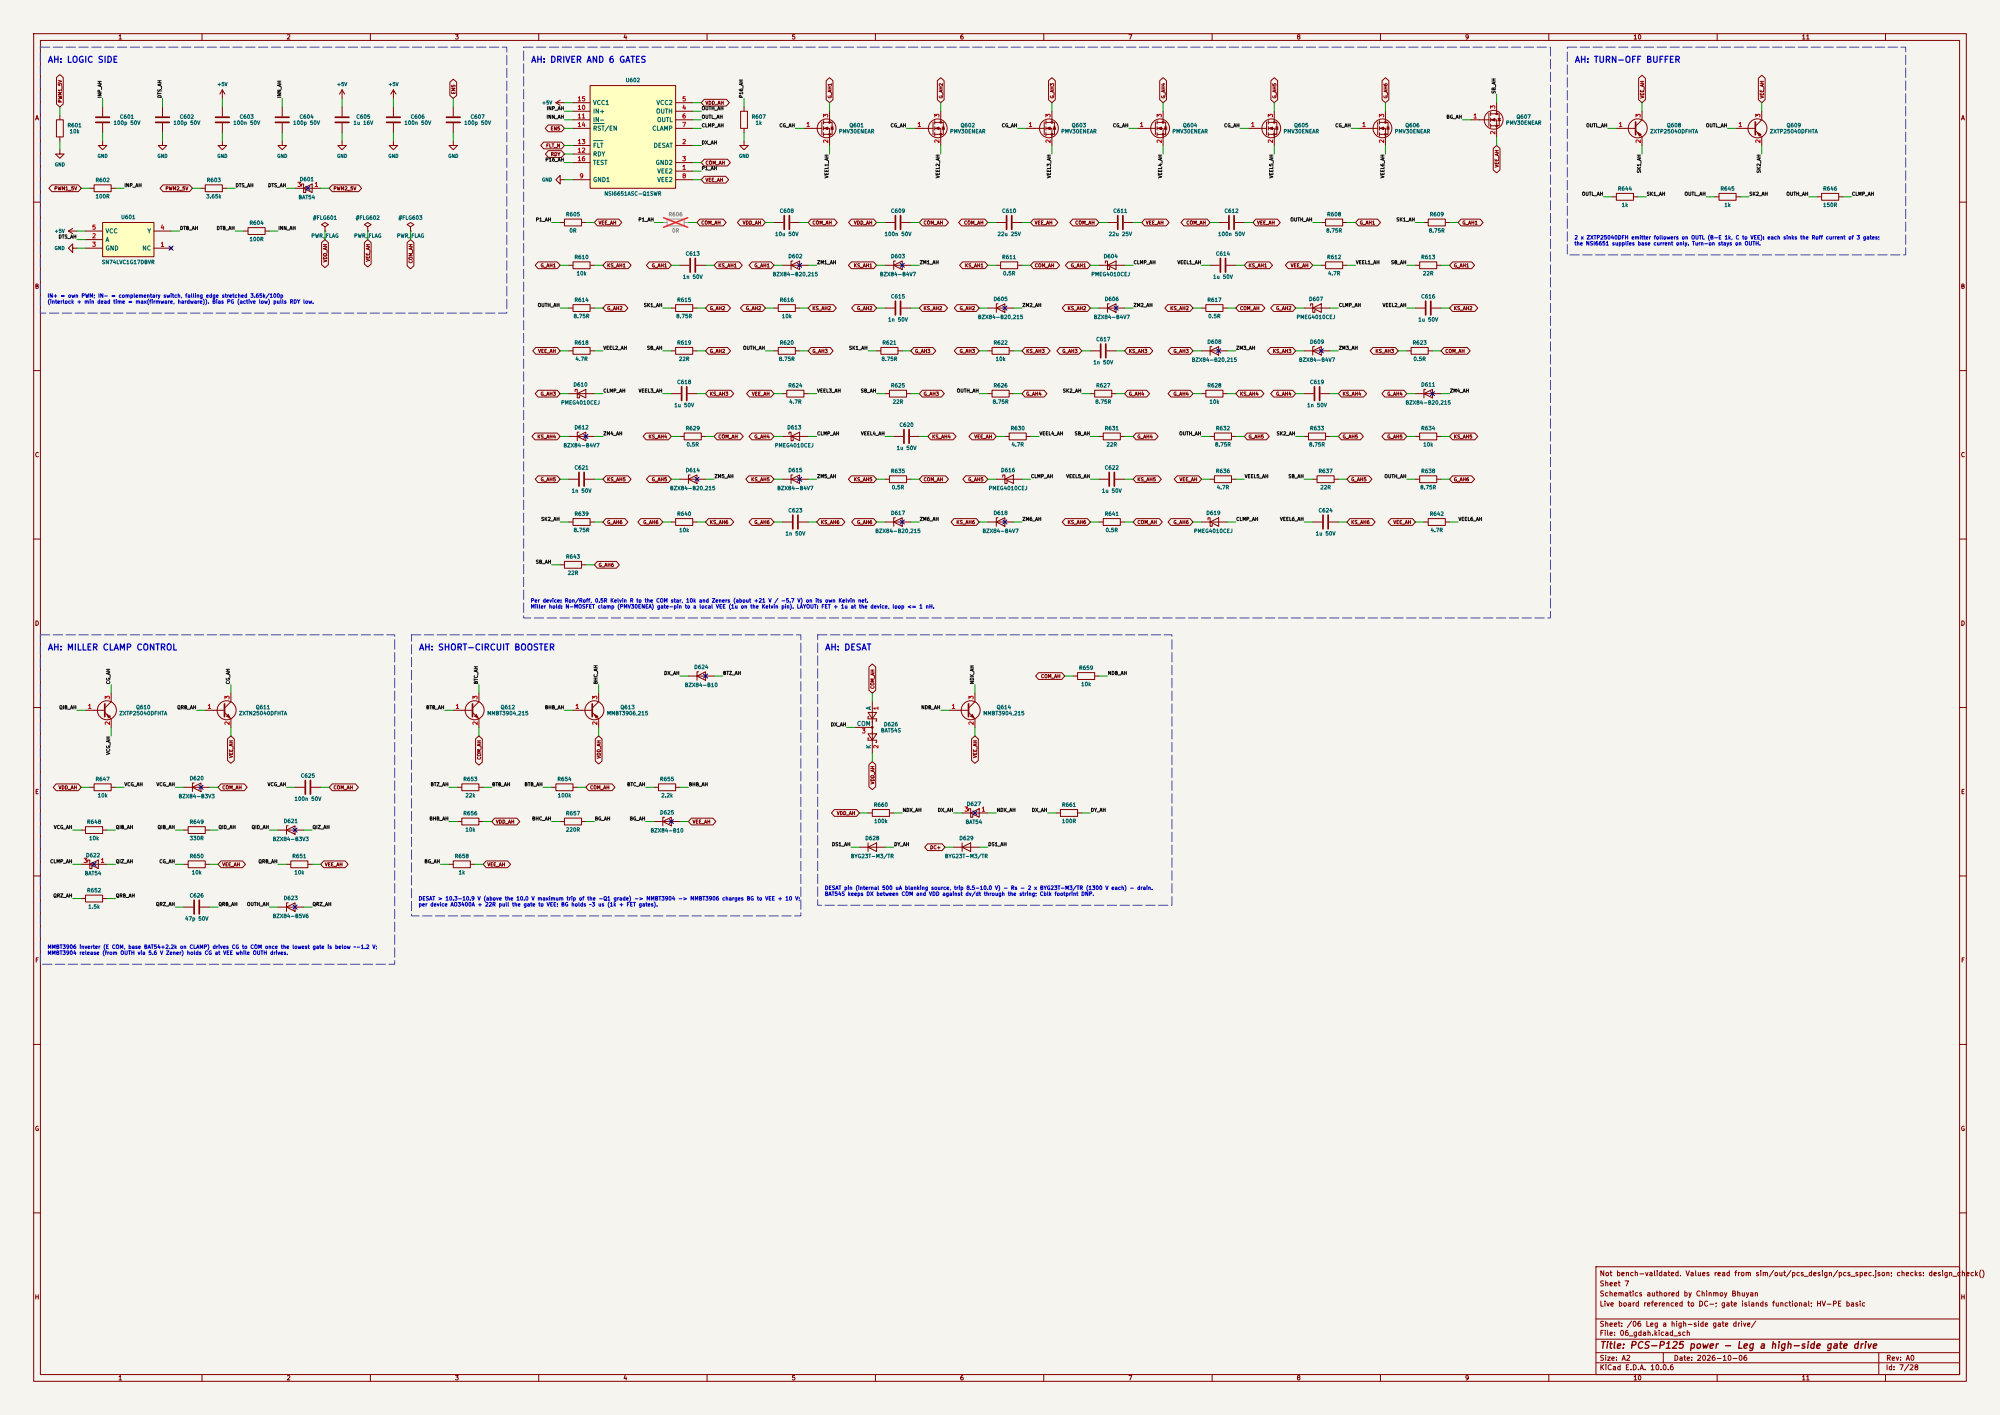
[picture p132: page 7]

IN+ = own PWM; IN- = complementary switch, falling edge stretched 3.65k/100p

Per device: Ron/Roff, 0.5R Kelvin R to the COM star, 10k and Zeners (about +21 V / -5.7 V) on its own Kelvin net. Miller hold: N-MOSFET clamp (PMV30ENEA) gate-pin to a local VEE (1u on the Kelvin pin). LAYOUT: FET + 1u at the device, loop <= 1 nH.

DESAT pin (internal 500 uA blanking source, trip 8.5-10.0 V) - Rs - 2 x BYG23T-M3/TR (1300 V each) - drain. BAT54S keeps DX between COM and VDD against dv/dt through the string; Cblk footprint DNP. AH: SHORT-CIRCUIT BOOSTER

Not bench-validated. Values read from sim/out/pcs_design/pcs_spec.json; checks: design_check()
Sheet 7
Schematics authored by Chinmoy Bhuyan
Live board referenced to DC-; gate islands functional; HV-PE basic

Sheet: /06 Leg a high-side gate drive/
File: 06_gdah.kicad_sch
Title: PCS-P125 power - Leg a high-side gate drive

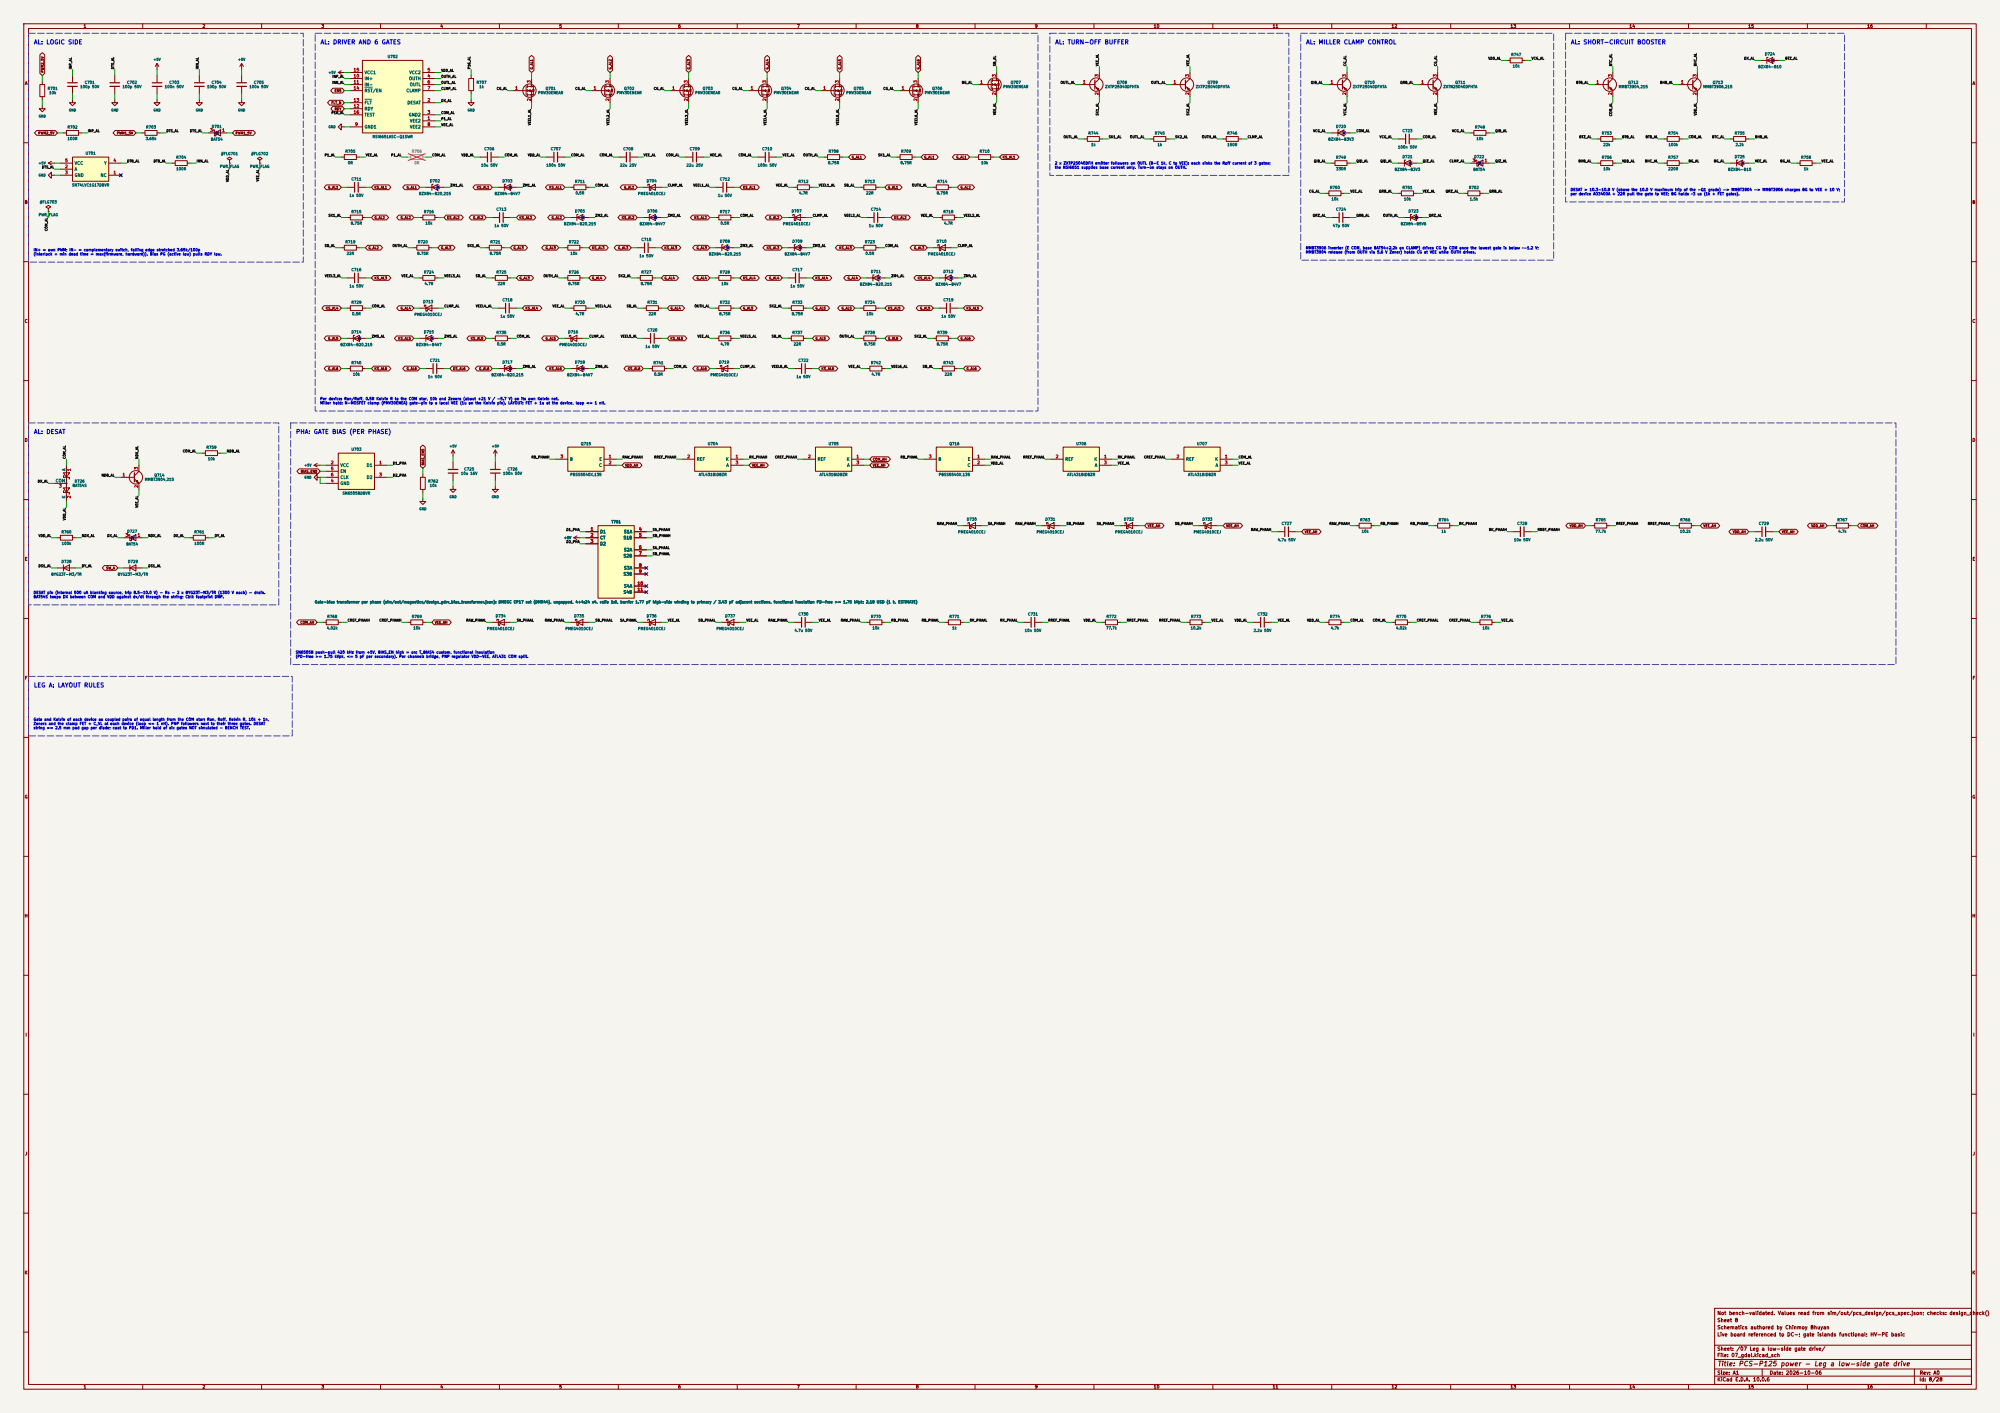
[picture p133: page 8]

AL: TURN-OFF BUFFER

DESAT > 10.3-10.9 V (above the 10.0 V maximum trip of the -Q1 grade) -> MMBT3904 -> MMBT3906 charges BG to VEE + 10 V; per device AO3400A + 22R pull the gate to VEE; BG holds ~3 us (1k + FET gates).

IN+ = own PWM; IN- = complementary switch, falling edge stretched 3.65k/100p
(interlock + min dead time = max(firmware, hardware)). Bias PG (active low) pulls RDY low.

MMBT3906 inverter (E COM, base BAT54+2.2k on CLAMP) drives CG to COM once the lowest gate is below ~-1.2 V; MMBT3904 release (from OUTH via 5.6 V Zener) holds CG at VEE while OUTH drives.

Per device: Ron/Roff, 0.5R Kelvin R to the COM star, 10k and Zeners (about +21 V / -5.7 V) on its own Kelvin net. Miller hold: N-MOSFET clamp (PMV30ENEA) gate-pin to a local VEE (1u on the Kelvin pin). LAYOUT: FET + 1u at the device, loop <= 1 nH. +5V

PHA: GATE BIAS (PER PHASE)

T701 Gate-bias transformer per phase (sim/out/magnetics/design_gdrv_bias_transformer.json): DMEGC EP17 set (DMR44), ungapped, 4+4:24 x4, ratio 1:6, barrier 1.77 pF high-side winding to primary / 3.43 pF adjacent sections, functional insulation PD-free >= 1.75 kVpk; 2.18 USD (1 k, ESTIMATE)

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

SN6505B push-pull 420 kHz from +5V, BIAS_EN high = on; T_BIAS4 custom, functional insulation
(PD-free >= 1.75 kVpk, <= 5 pF per secondary). Per channel: bridge, PNP regulator VDD-VEE, ATL431 COM split.

Gate and Kelvin of each device as coupled pairs of equal length from the COM star; Ron, Roff, Kelvin R, 10k + 1n, Zeners and the clamp FET + C_VL at each device (loop <= 1 nH). PNP followers next to their three gates. DESAT string >= 2.5 mm pad gap per diode; coat to PD1. Miller hold of six gates NOT simulated - BENCH TEST. LEG A: LAYOUT RULES

Not bench-validated. Values read from sim/out/pcs_design/pcs_spec.json; checks: design_check()
Sheet 8
Schematics authored by Chinmoy Bhuyan
Live board referenced to DC-; gate islands functional; HV-PE basic

Sheet: /07 Leg a low-side gate drive/
File: 07_gdal.kicad_sch
Title: PCS-P125 power - Leg a low-side gate drive

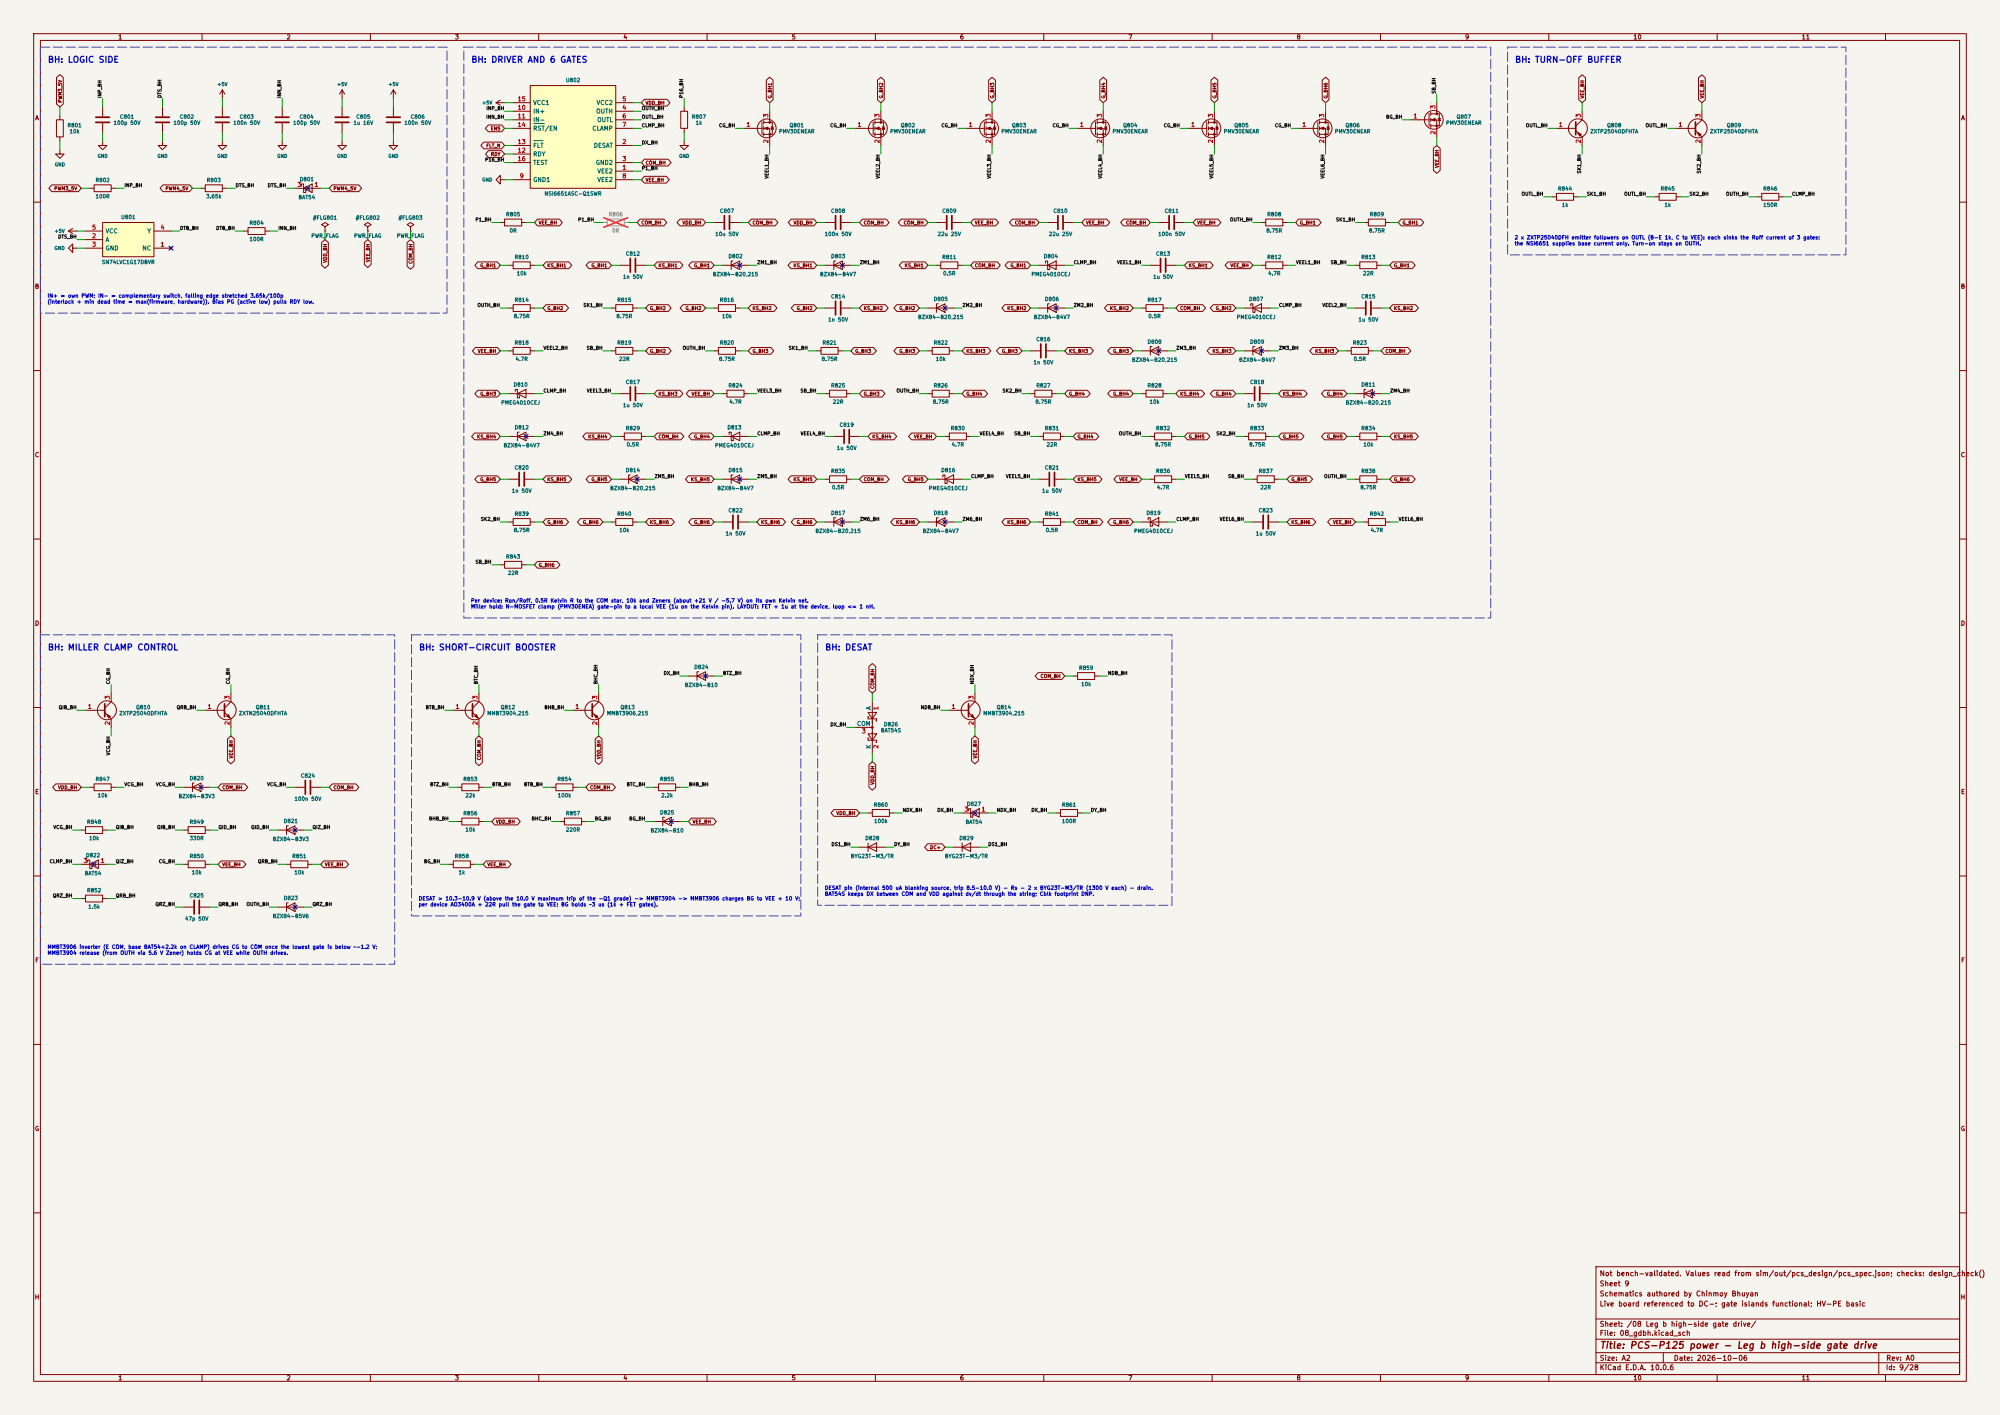
[picture p134: page 9]

BH: DRIVER AND 6 GATES
U802 NSI6651ASC-Q1SWR

2 x ZXTP25040DFH emitter followers on OUTL (B-E 1k, C to VEE): each sinks the Roff current of 3 gates; the NSI6651 supplies base current only. Turn-on stays on OUTH.

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

ZM6_BH DESAT pin (internal 500 uA blanking source, trip 8.5-10.0 V) - Rs - 2 x BYG23T-M3/TR (1300 V each) - drain. BAT54S keeps DX between COM and VDD against dv/dt through the string; Cblk footprint DNP. MMBT3906 inverter (E COM, base BAT54+2.2k on CLAMP) drives CG to COM once the lowest gate is below ~-1.2 V; MMBT3904 release (from OUTH via 5.6 V Zener) holds CG at VEE while OUTH drives.

Per device: Ron/Roff, 0.5R Kelvin R to the COM star, 10k and Zeners (about +21 V / -5.7 V) on its own Kelvin net. Miller hold: N-MOSFET clamp (PMV30ENEA) gate-pin to a local VEE (1u on the Kelvin pin). LAYOUT: FET + 1u at the device, loop <= 1 nH. BH: MILLER CLAMP CONTROL

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

Not bench-validated. Values read from sim/out/pcs_design/pcs_spec.json; checks: design_check()
Sheet 9
Schematics authored by Chinmoy Bhuyan
Live board referenced to DC-; gate islands functional; HV-PE basic

Sheet: /08 Leg b high-side gate drive/
File: 08_gdbh.kicad_sch
Title: PCS-P125 power - Leg b high-side gate drive

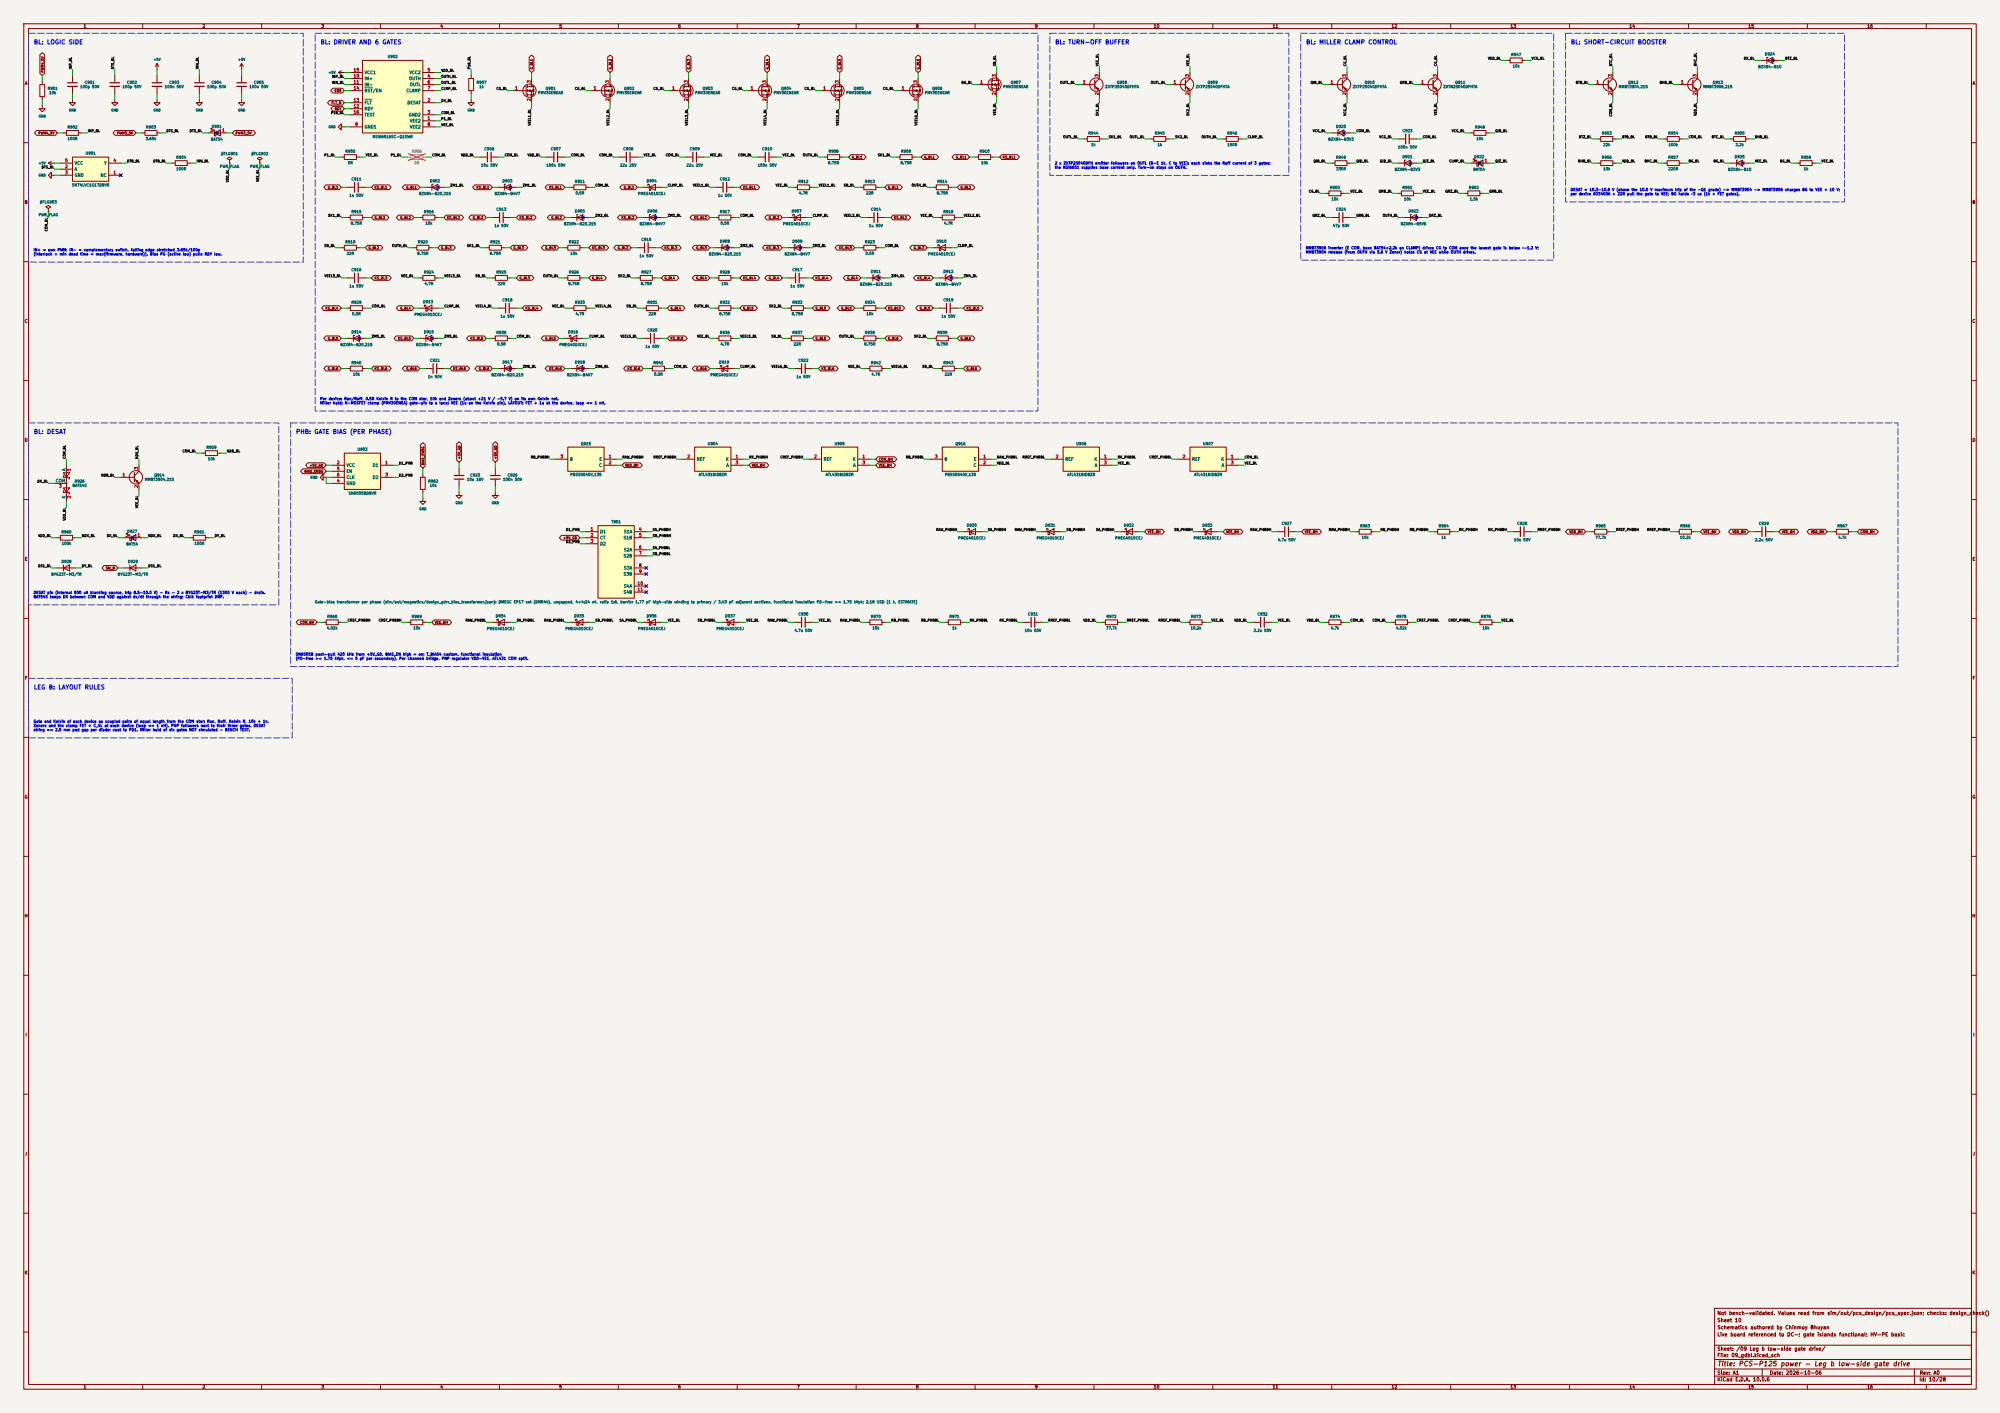
[picture p135: page 10]

BL: MILLER CLAMP CONTROL

IN+ = own PWM; IN- = complementary switch, falling edge stretched 3.65k/100p

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

PHB: GATE BIAS (PER PHASE)

T901 Gate-bias transformer per phase (sim/out/magnetics/design_gdrv_bias_transformer.json): DMEGC EP17 set (DMR44), ungapped, 4+4:24 x4, ratio 1:6, barrier 1.77 pF high-side winding to primary / 3.43 pF adjacent sections, functional insulation PD-free >= 1.75 kVpk; 2.18 USD (1 k, ESTIMATE)

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

SN6505B push-pull 420 kHz from +5V_GD, BIAS_EN high = on; T_BIAS4 custom, functional insulation
(PD-free >= 1.75 kVpk, <= 5 pF per secondary). Per channel: bridge, PNP regulator VDD-VEE, ATL431 COM split.

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

Not bench-validated. Values read from sim/out/pcs_design/pcs_spec.json; checks: design_check()
Sheet 10
Schematics authored by Chinmoy Bhuyan
Live board referenced to DC-; gate islands functional; HV-PE basic

Sheet: /09 Leg b low-side gate drive/
File: 09_gdbl.kicad_sch
Title: PCS-P125 power - Leg b low-side gate drive

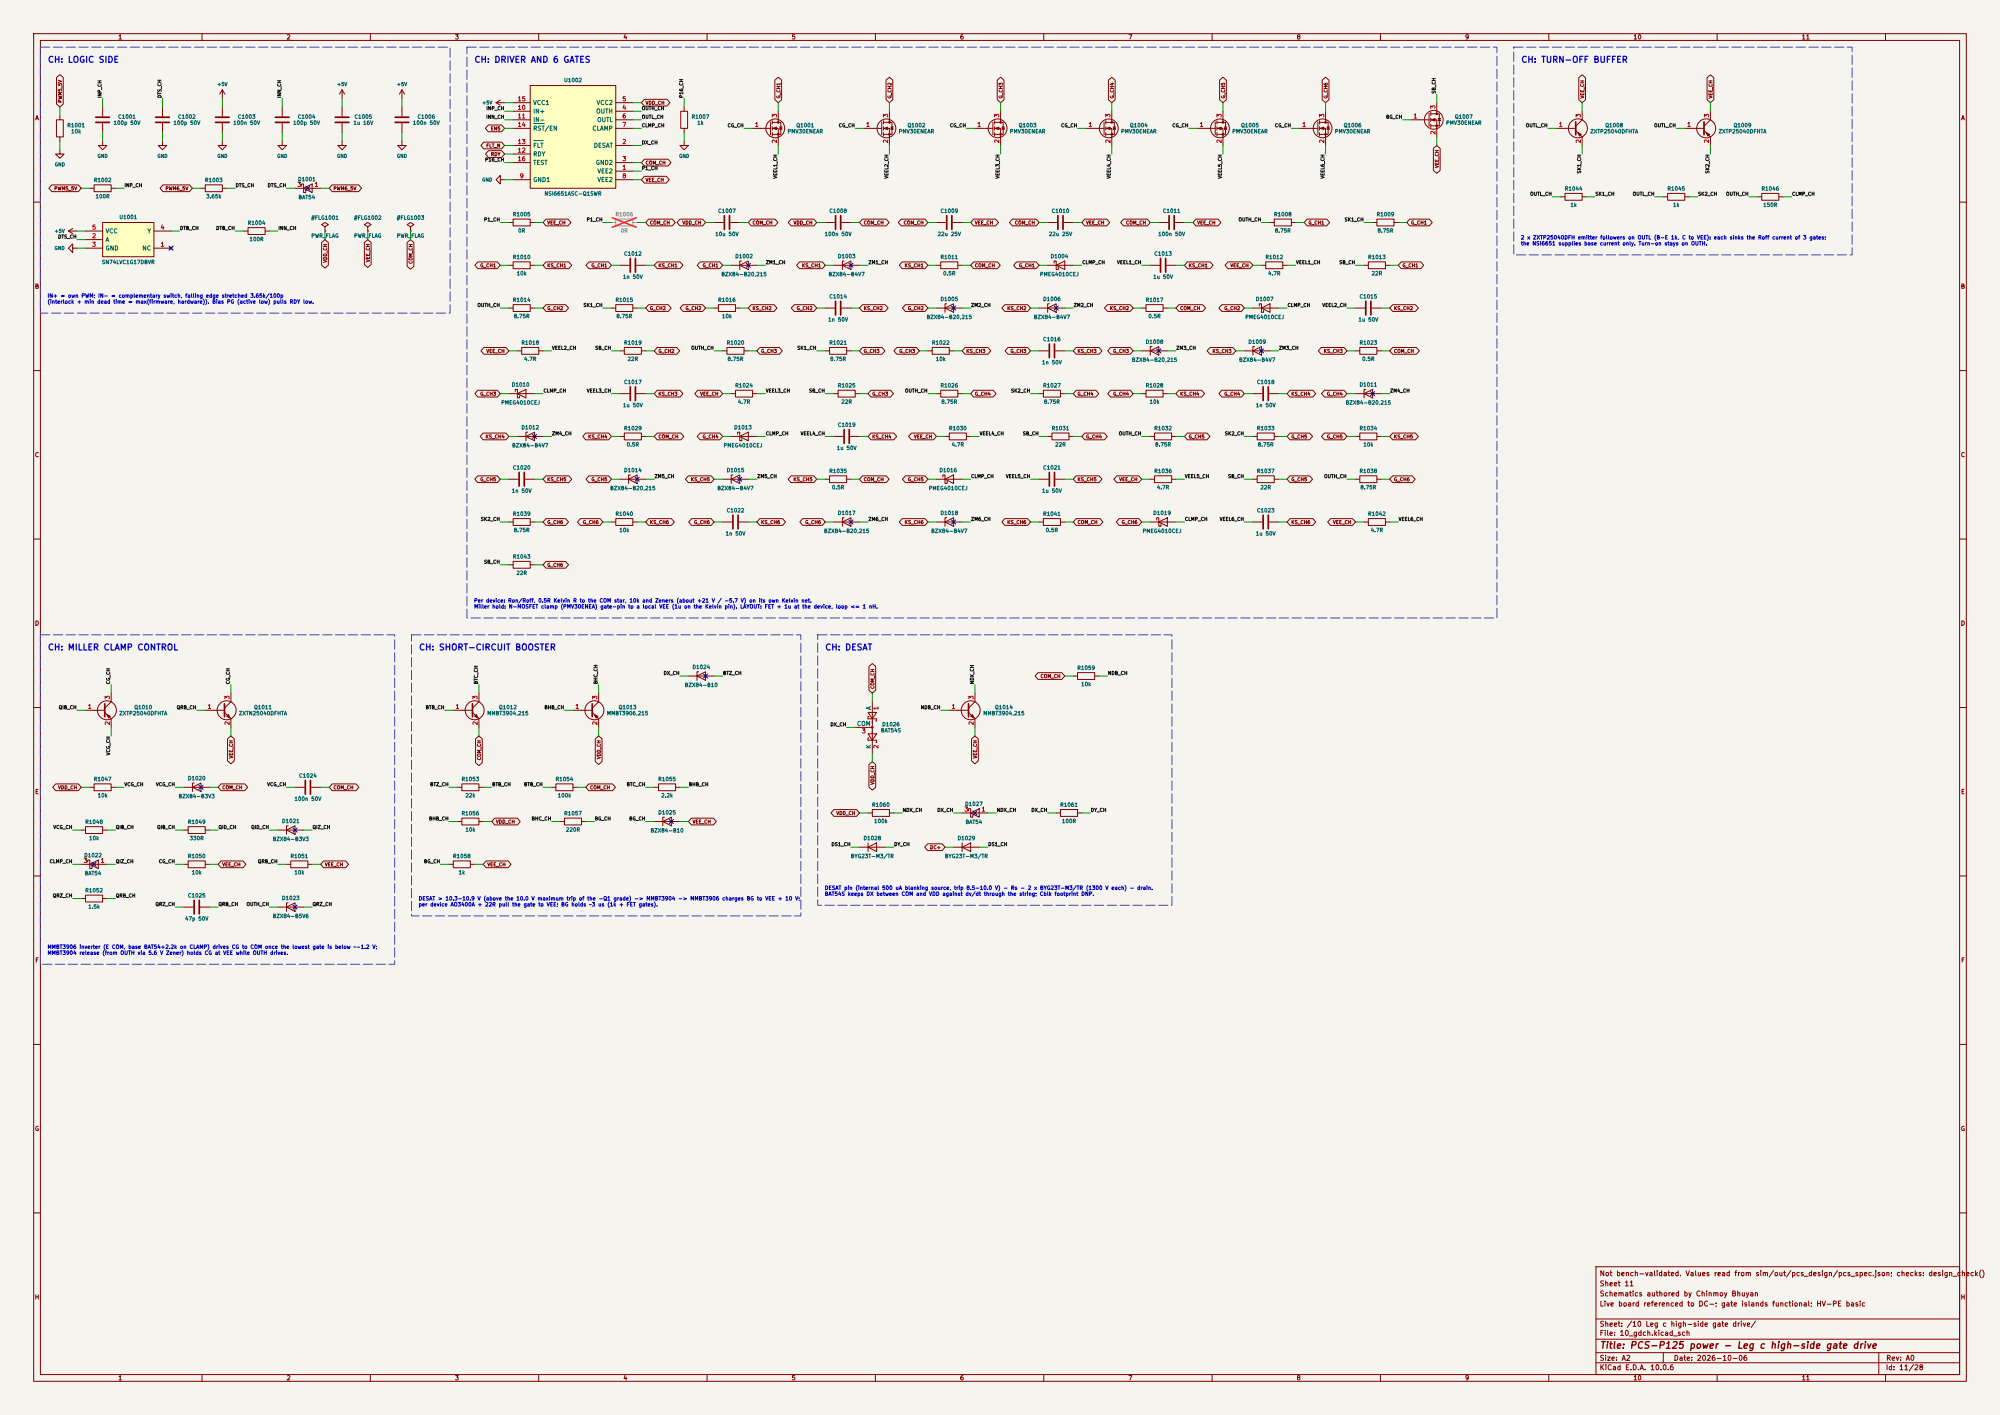
[picture p136: page 11]

CH: DRIVER AND 6 GATES
U1002 NSI6651ASC-Q1SWR

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

IN+ = own PWM; IN- = complementary switch, falling edge stretched 3.65k/100p

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

Not bench-validated. Values read from sim/out/pcs_design/pcs_spec.json; checks: design_check()
Sheet 11
Schematics authored by Chinmoy Bhuyan
Live board referenced to DC-; gate islands functional; HV-PE basic

Sheet: /10 Leg c high-side gate drive/
File: 10_gdch.kicad_sch
Title: PCS-P125 power - Leg c high-side gate drive

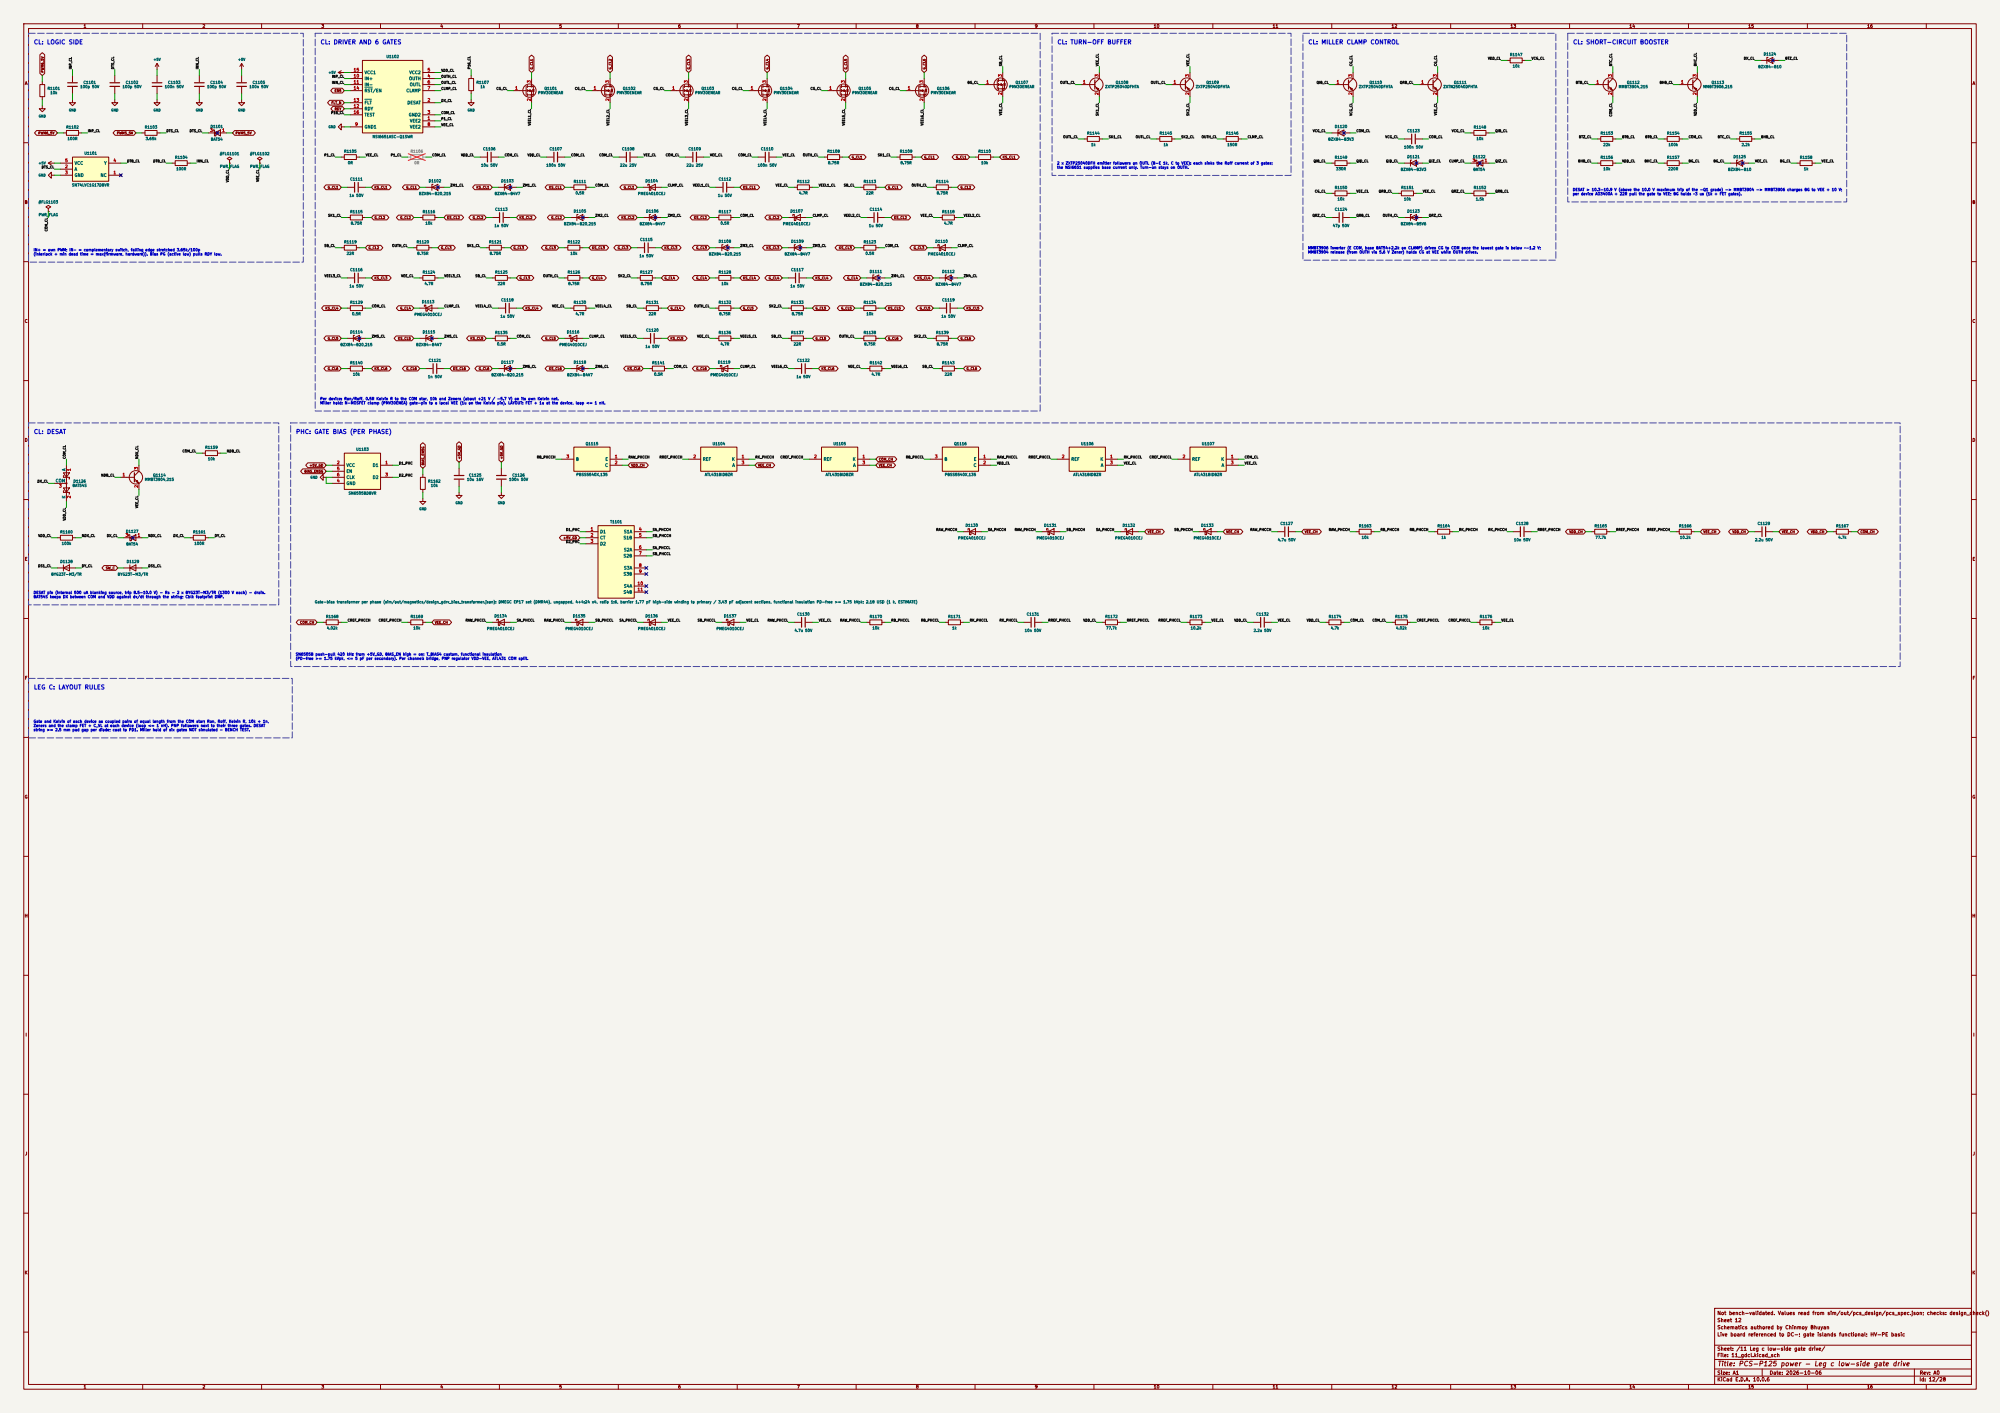
[picture p137: page 12]

CL: TURN-OFF BUFFER

CL: MILLER CLAMP CONTROL

CL: SHORT-CIRCUIT BOOSTER

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

MMBT3906 inverter (E COM, base BAT54+2.2k on CLAMP) drives CG to COM once the lowest gate is below ~-1.2 V; MMBT3904 release (from OUTH via 5.6 V Zener) holds CG at VEE while OUTH drives. IN+ = own PWM; IN- = complementary switch, falling edge stretched 3.65k/100p

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

Gate and Kelvin of each device as coupled pairs of equal length from the COM star; Ron, Roff, Kelvin R, 10k + 1n, Zeners and the clamp FET + C_VL at each device (loop <= 1 nH). PNP followers next to their three gates. DESAT string >= 2.5 mm pad gap per diode; coat to PD1. Miller hold of six gates NOT simulated - BENCH TEST. DESAT pin (internal 500 uA blanking source, trip 8.5-10.0 V) - Rs - 2 x BYG23T-M3/TR (1300 V each) - drain. BAT54S keeps DX between COM and VDD against dv/dt through the string; Cblk footprint DNP.

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

Not bench-validated. Values read from sim/out/pcs_design/pcs_spec.json; checks: design_check()
Sheet 12
Schematics authored by Chinmoy Bhuyan
Live board referenced to DC-; gate islands functional; HV-PE basic

Sheet: /11 Leg c low-side gate drive/
File: 11_gdcl.kicad_sch
Title: PCS-P125 power - Leg c low-side gate drive

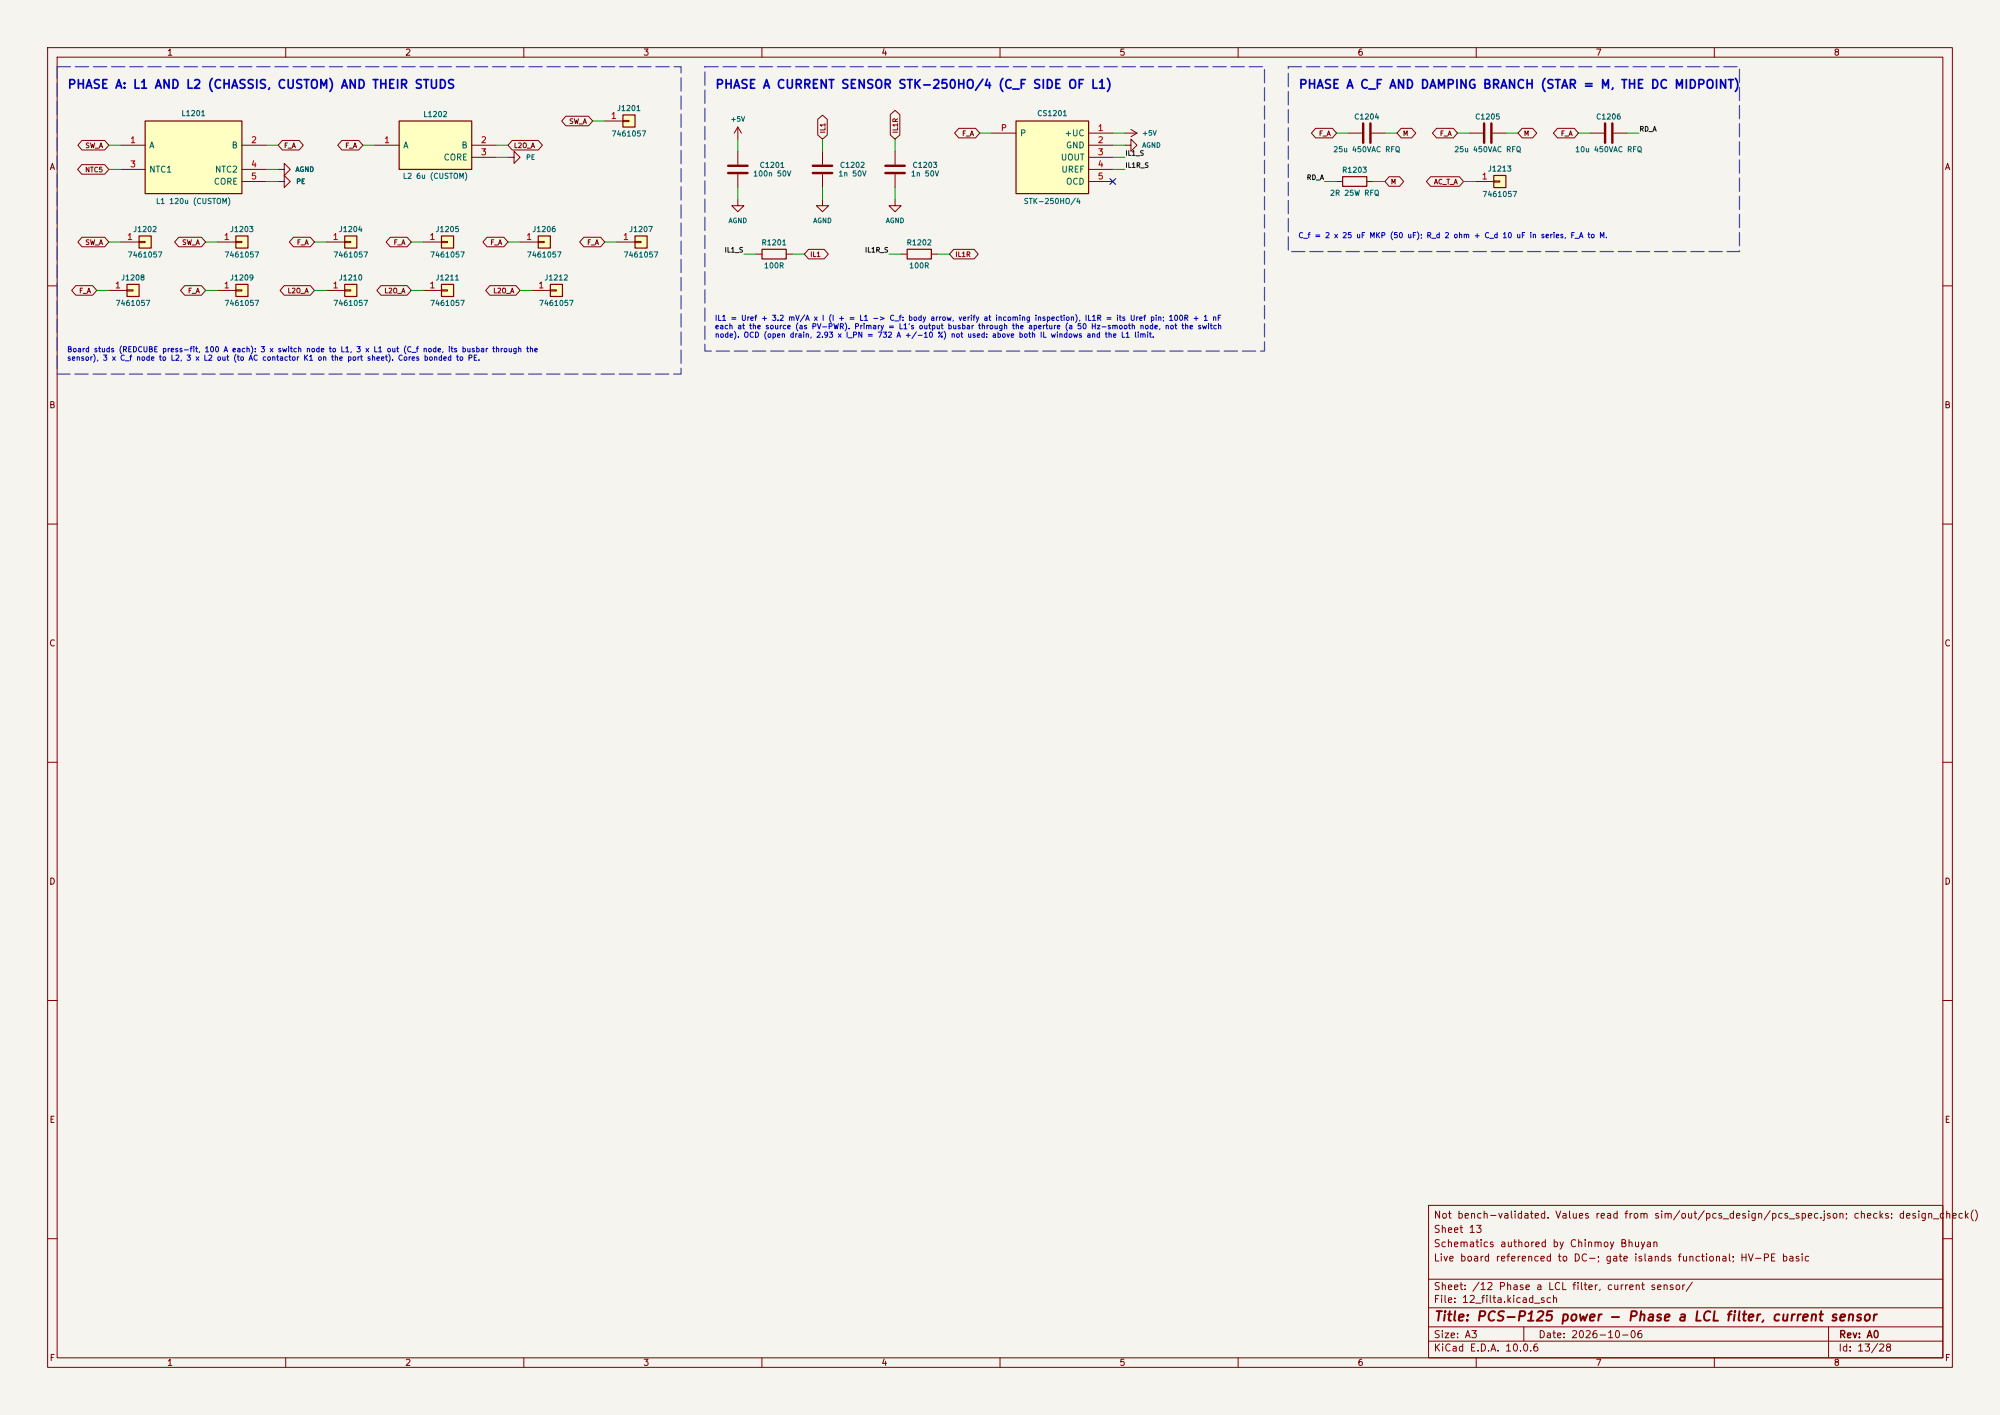
[picture p138: page 13]

C_f = 2 x 25 uF MKP (50 uF); R_d 2 ohm + C_d 10 uF in series, F_A to M. PHASE A CURRENT SENSOR STK-250HO/4 (C_F SIDE OF L1)

IL1R_S Board studs (REDCUBE press-fit, 100 A each): 3 x switch node to L1, 3 x L1 out (C_f node, its busbar through the

IL1 = Uref + 3.2 mV/A x I (I + = L1 -> C_f: body arrow, verify at incoming inspection), IL1R = its Uref pin; 100R + 1 nF
each at the source (as PV-PWR). Primary = L1's output busbar through the aperture (a 50 Hz-smooth node, not the switch

sensor), 3 x C_f node to L2, 3 x L2 out (to AC contactor K1 on the port sheet). Cores bonded to PE.

Not bench-validated. Values read from sim/out/pcs_design/pcs_spec.json; checks: design_check()
Sheet 13
Schematics authored by Chinmoy Bhuyan
Live board referenced to DC-; gate islands functional; HV-PE basic

Sheet: /12 Phase a LCL filter, current sensor/
File: 12_filta.kicad_sch
Title: PCS-P125 power - Phase a LCL filter, current sensor

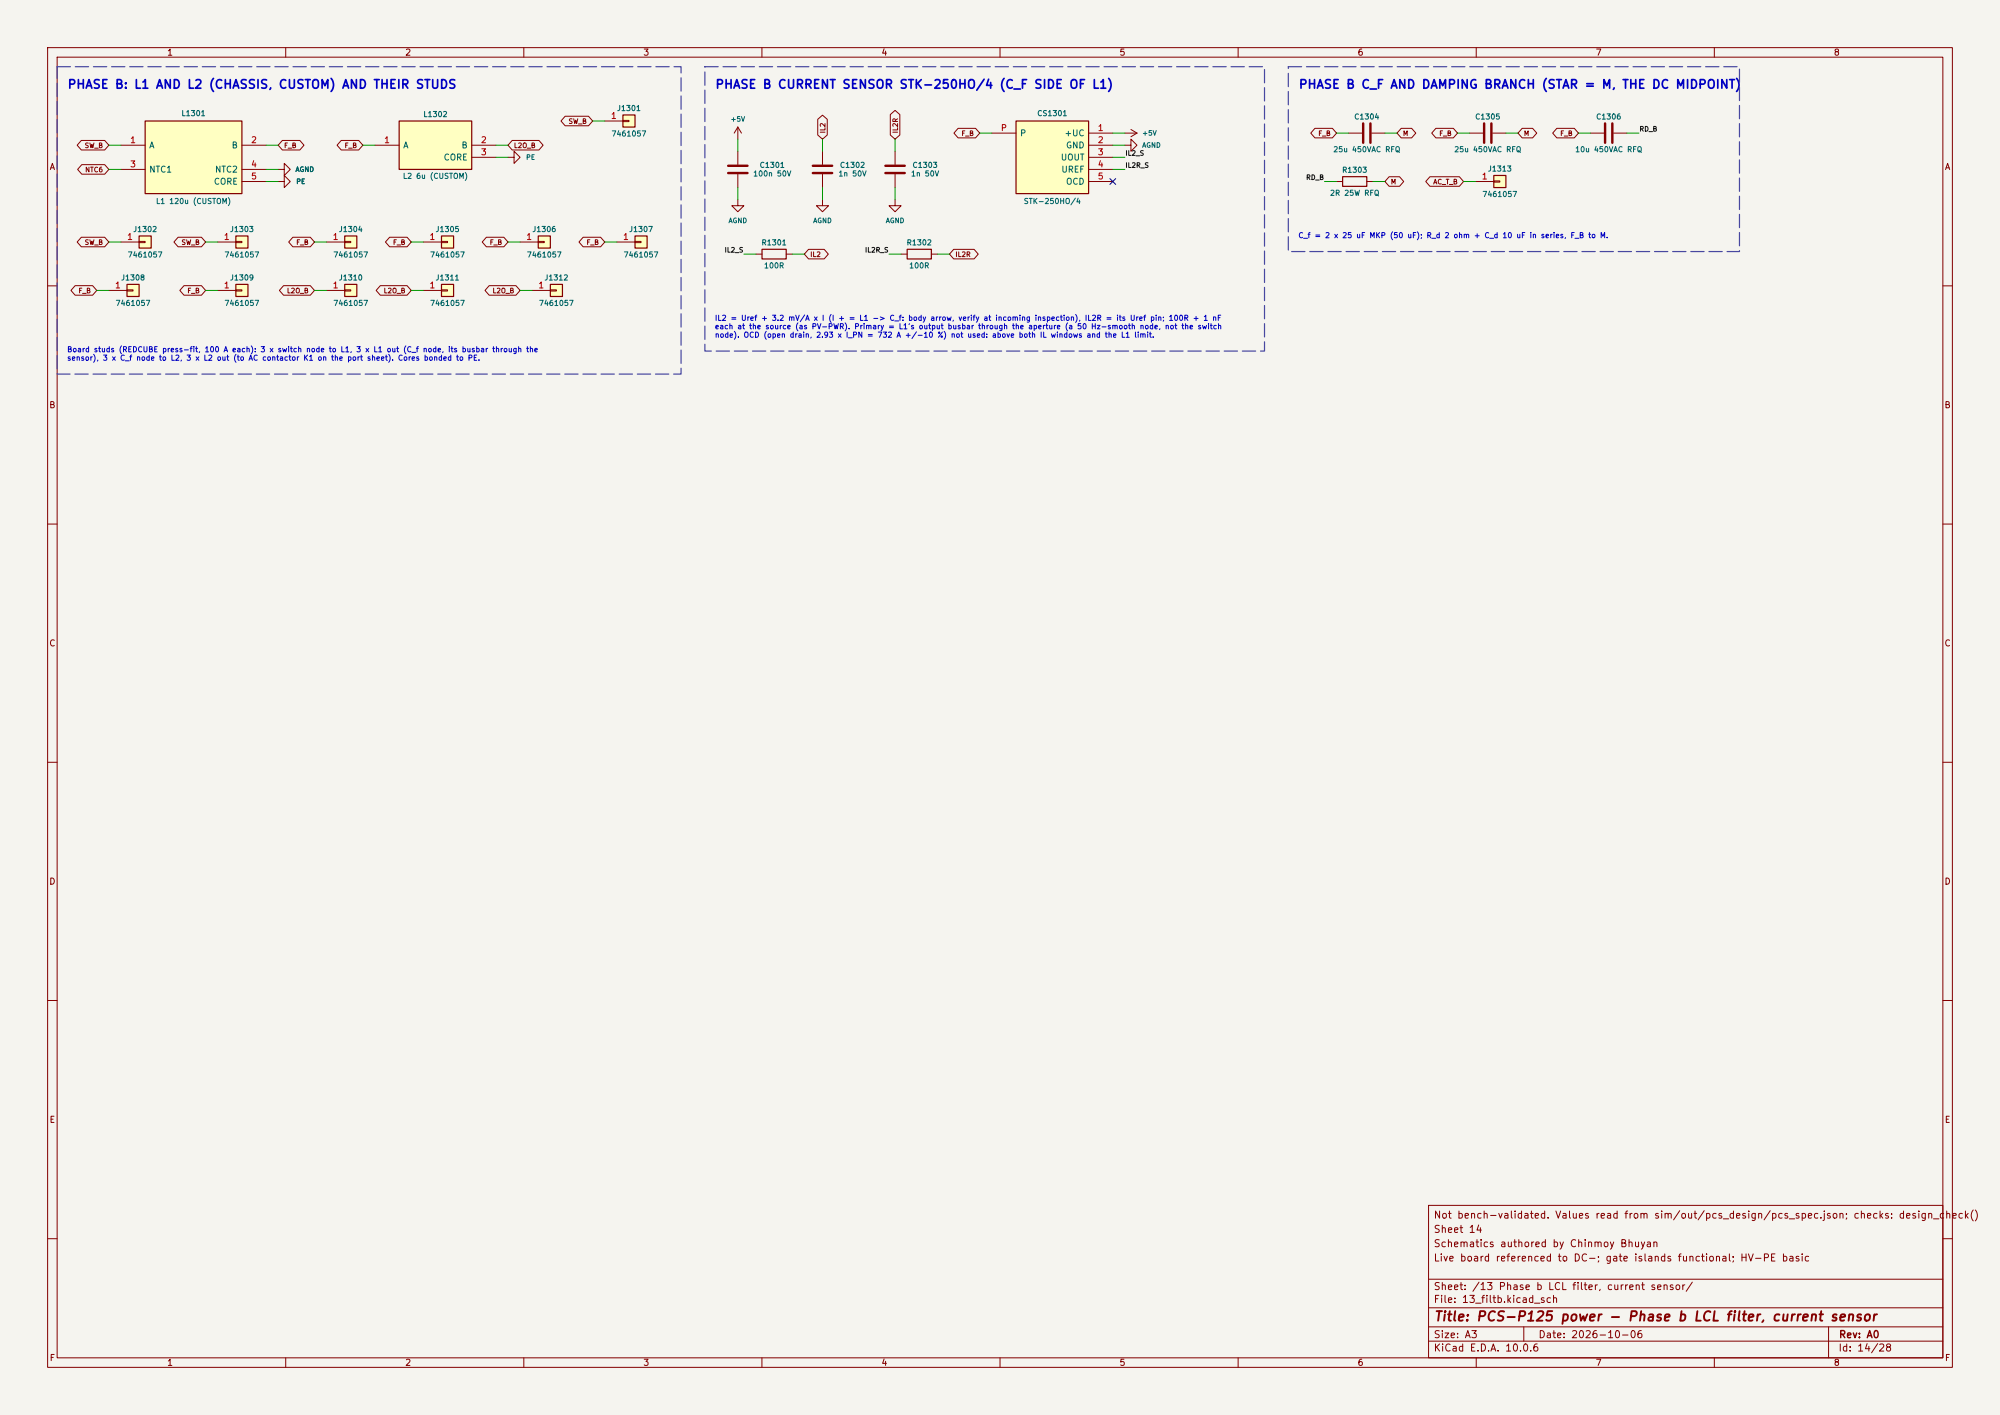
[picture p139: page 14]

sensor), 3 x C_f node to L2, 3 x L2 out (to AC contactor K1 on the port sheet). Cores bonded to PE. PHASE B: L1 AND L2 (CHASSIS, CUSTOM) AND THEIR STUDS

C_f = 2 x 25 uF MKP (50 uF); R_d 2 ohm + C_d 10 uF in series, F_B to M. PHASE B C_F AND DAMPING BRANCH (STAR = M, THE DC MIDPOINT)

node). OCD (open drain, 2.93 x I_PN = 732 A +/-10 %) not used: above both IL windows and the L1 limit. PE

IL2 = Uref + 3.2 mV/A x I (I + = L1 -> C_f: body arrow, verify at incoming inspection), IL2R = its Uref pin; 100R + 1 nF
each at the source (as PV-PWR). Primary = L1's output busbar through the aperture (a 50 Hz-smooth node, not the switch

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

Not bench-validated. Values read from sim/out/pcs_design/pcs_spec.json; checks: design_check()
Sheet 14
Schematics authored by Chinmoy Bhuyan
Live board referenced to DC-; gate islands functional; HV-PE basic

Sheet: /13 Phase b LCL filter, current sensor/
File: 13_filtb.kicad_sch
Title: PCS-P125 power - Phase b LCL filter, current sensor

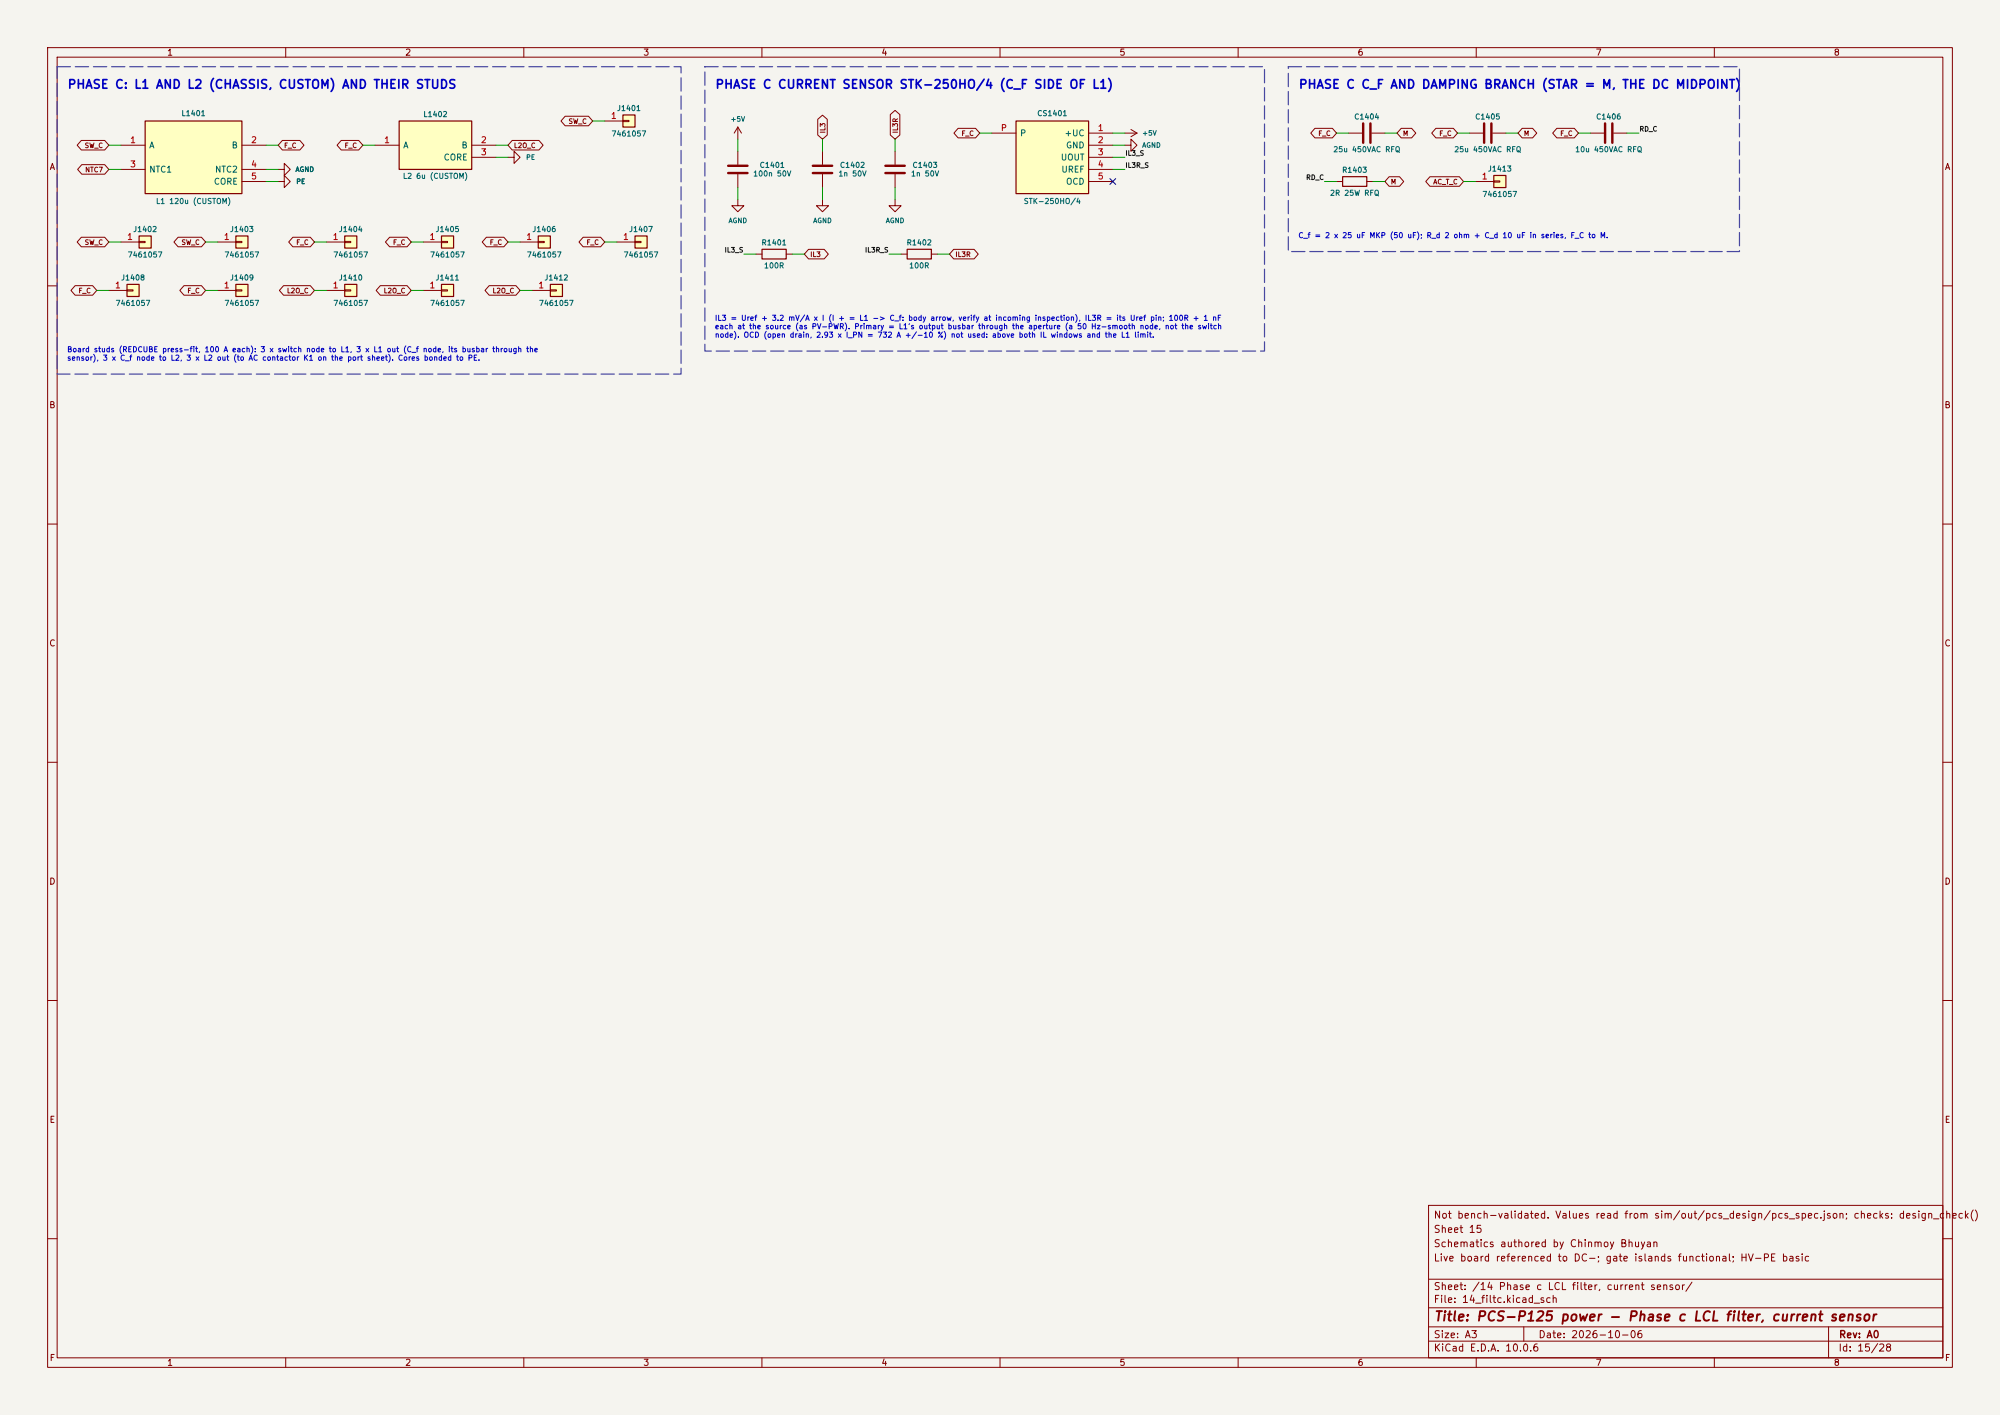
[picture p140: page 15]

node). OCD (open drain, 2.93 x I_PN = 732 A +/-10 %) not used: above both IL windows and the L1 limit. PHASE C CURRENT SENSOR STK-250HO/4 (C_F SIDE OF L1)

AGND
C_f = 2 x 25 uF MKP (50 uF); R_d 2 ohm + C_d 10 uF in series, F_C to M. PE

IL3 = Uref + 3.2 mV/A x I (I + = L1 -> C_f: body arrow, verify at incoming inspection), IL3R = its Uref pin; 100R + 1 nF
each at the source (as PV-PWR). Primary = L1's output busbar through the aperture (a 50 Hz-smooth node, not the switch

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

Not bench-validated. Values read from sim/out/pcs_design/pcs_spec.json; checks: design_check()
Sheet 15
Schematics authored by Chinmoy Bhuyan
Live board referenced to DC-; gate islands functional; HV-PE basic

Sheet: /14 Phase c LCL filter, current sensor/
File: 14_filtc.kicad_sch
Title: PCS-P125 power - Phase c LCL filter, current sensor

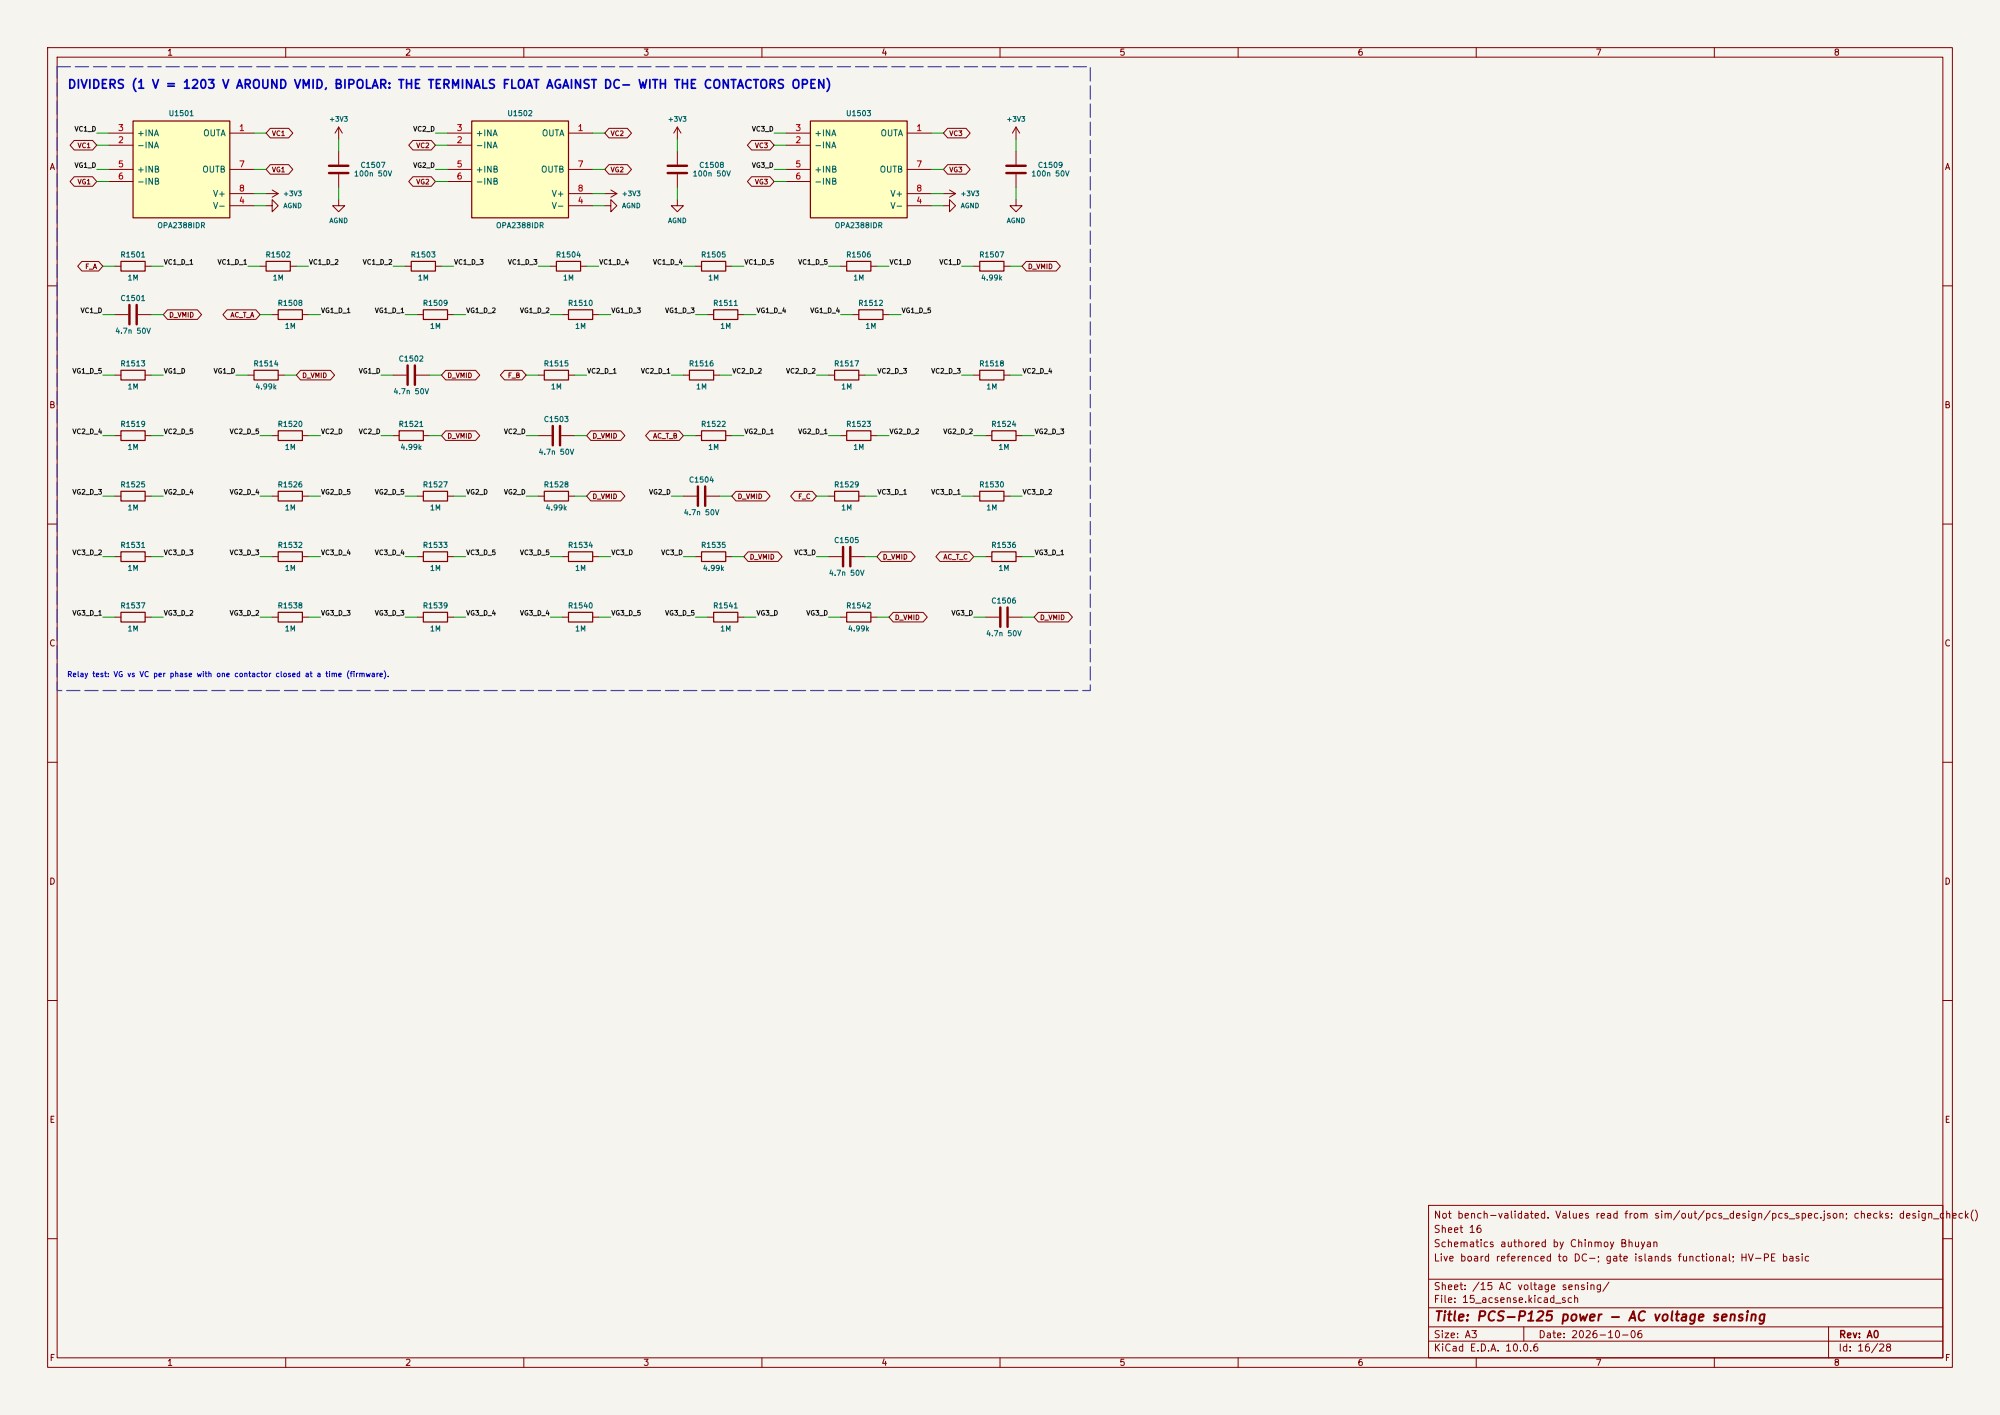
[picture p141: page 16]

Relay test: VG vs VC per phase with one contactor closed at a time (firmware).

Not bench-validated. Values read from sim/out/pcs_design/pcs_spec.json; checks: design_check()
Sheet 16
Schematics authored by Chinmoy Bhuyan
Live board referenced to DC-; gate islands functional; HV-PE basic

Sheet: /15 AC voltage sensing/
File: 15_acsense.kicad_sch
Title: PCS-P125 power - AC voltage sensing

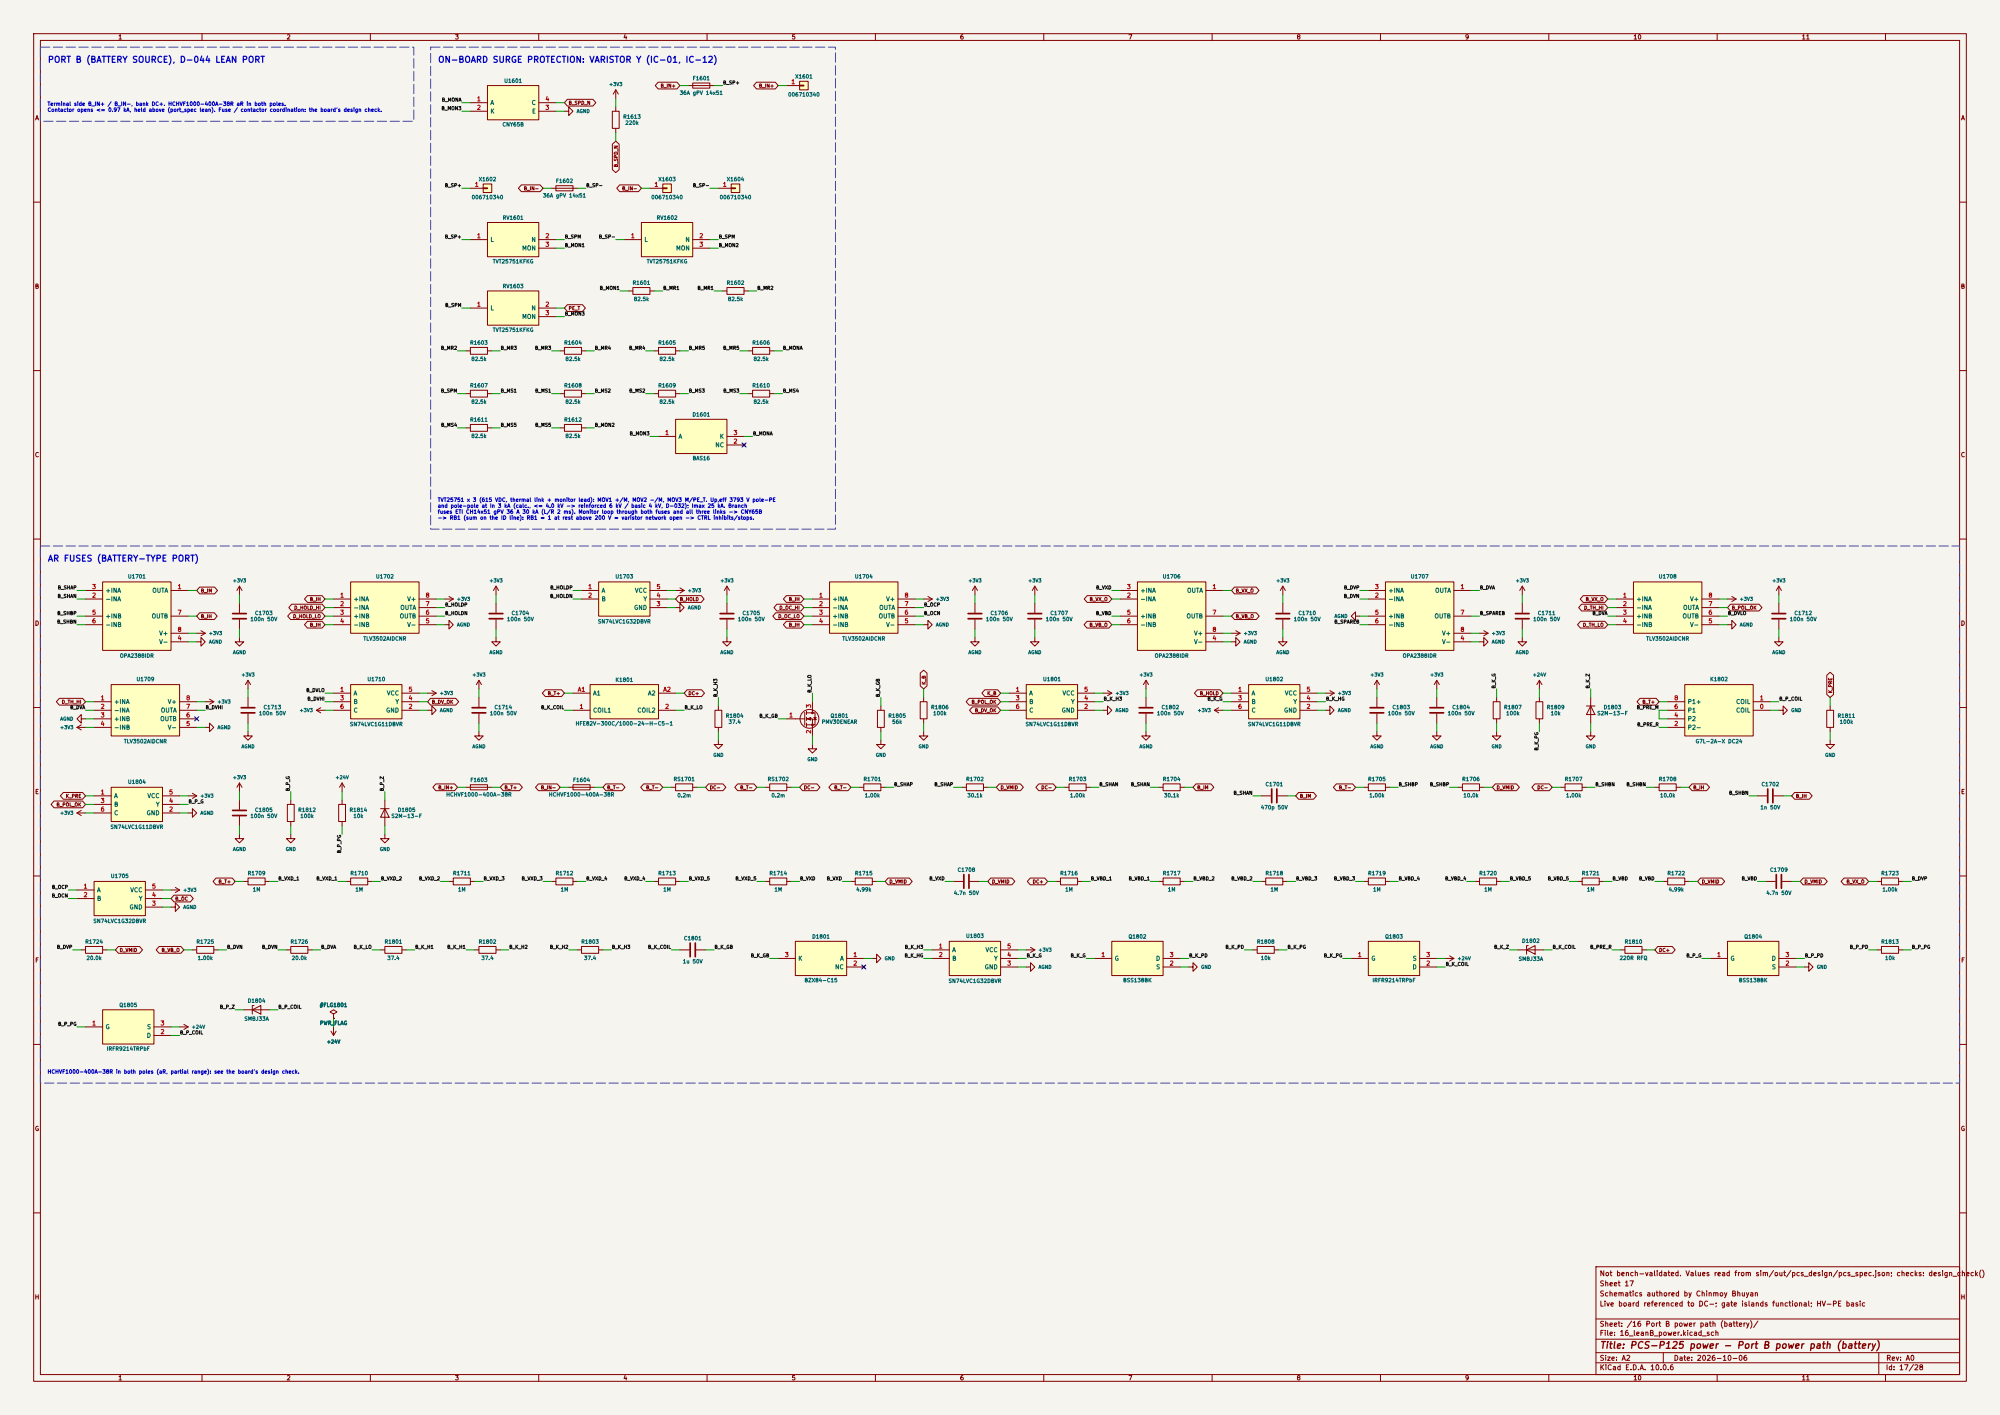
[picture p142: page 17]

Terminal side B_IN+ / B_IN-, bank DC+. HCHVF1000-400A-38R aR in both poles. Contactor opens <= 0.97 kA, held above (port_spec lean). Fuse / contactor coordination: the board's design check.

TVT25751 x 3 (615 VDC, thermal link + monitor lead): MOV1 +/M, MOV2 -/M, MOV3 M/PE_T. Up,eff 3793 V pole-PE
and pole-pole at In 3 kA (calc., <= 4.0 kV -> reinforced 6 kV / basic 4 kV, D-032); Imax 25 kA. Branch
fuses ETI CH14x51 gPV 36 A 30 kA (L/R 2 ms). Monitor loop through both fuses and all three links -> CNY65B -> RB1 (sum on the ID line): RB1 = 1 at rest above 200 V = varistor network open -> CTRL inhibits/stops.

AR FUSES (BATTERY-TYPE PORT)
U1701 OPA2388IDR

HCHVF1000-400A-38R in both poles (aR, partial range): see the board's design check.

Not bench-validated. Values read from sim/out/pcs_design/pcs_spec.json; checks: design_check()
Sheet 17
Schematics authored by Chinmoy Bhuyan
Live board referenced to DC-; gate islands functional; HV-PE basic

Sheet: /16 Port B power path (battery)/
File: 16_leanB_power.kicad_sch
Title: PCS-P125 power - Port B power path (battery)

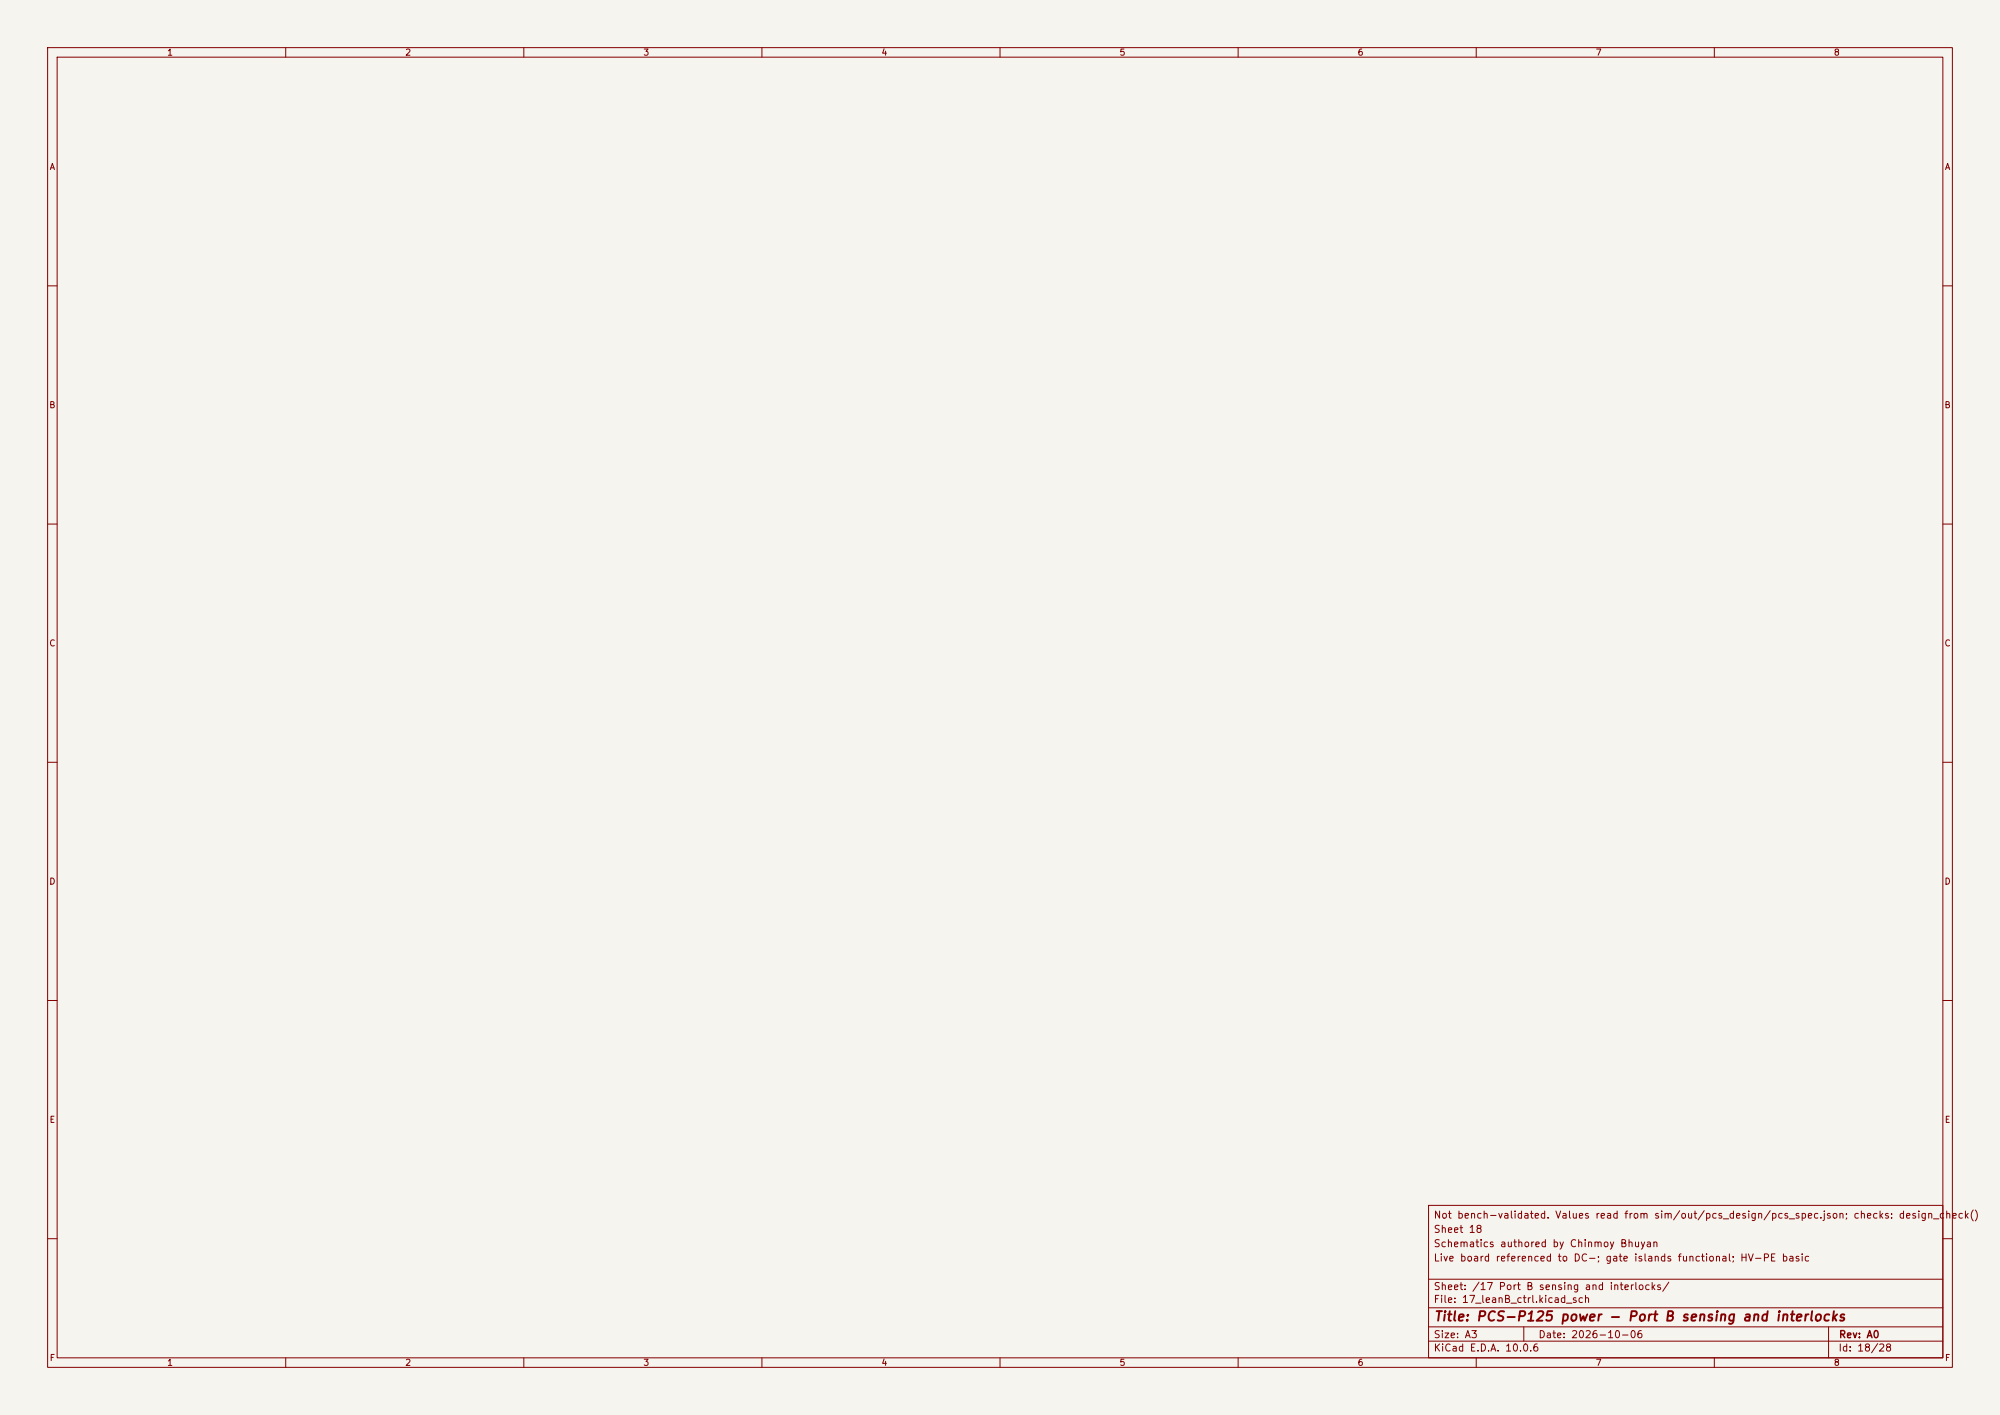
[picture p143: page 18]

Not bench-validated. Values read from sim/out/pcs_design/pcs_spec.json; checks: design_check()
Sheet 18
Schematics authored by Chinmoy Bhuyan
Live board referenced to DC-; gate islands functional; HV-PE basic

Sheet: /17 Port B sensing and interlocks/
File: 17_leanB_ctrl.kicad_sch
Title: PCS-P125 power - Port B sensing and interlocks

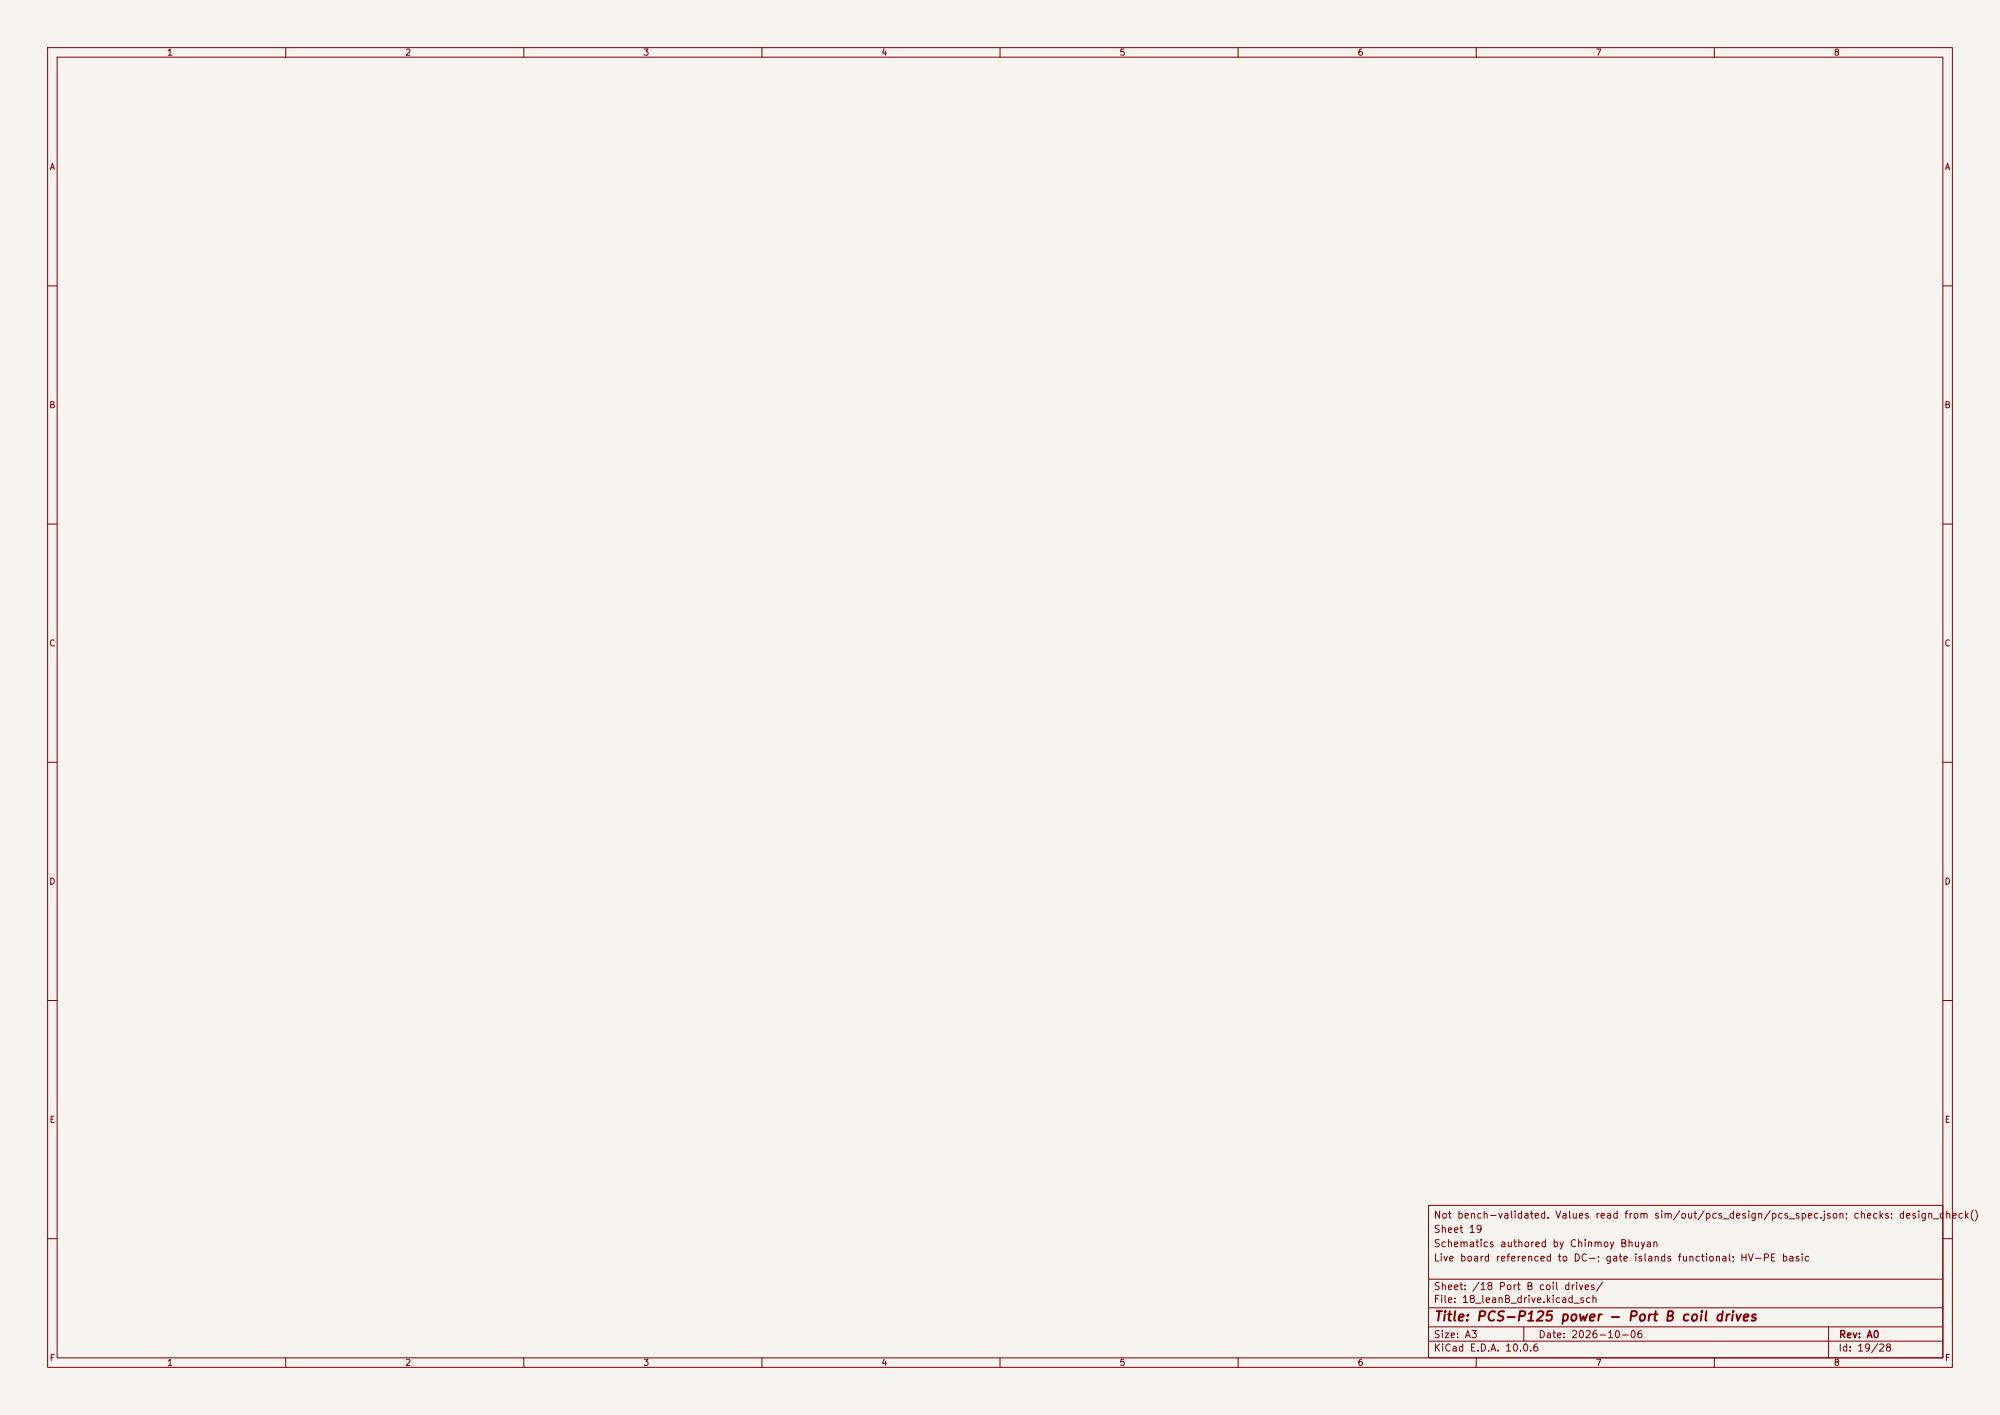
[picture p144: page 19]

Not bench-validated. Values read from sim/out/pcs_design/pcs_spec.json; checks: design_check()
Sheet 19
Schematics authored by Chinmoy Bhuyan
Live board referenced to DC-; gate islands functional; HV-PE basic

Sheet: /18 Port B coil drives/
File: 18_leanB_drive.kicad_sch
Title: PCS-P125 power - Port B coil drives

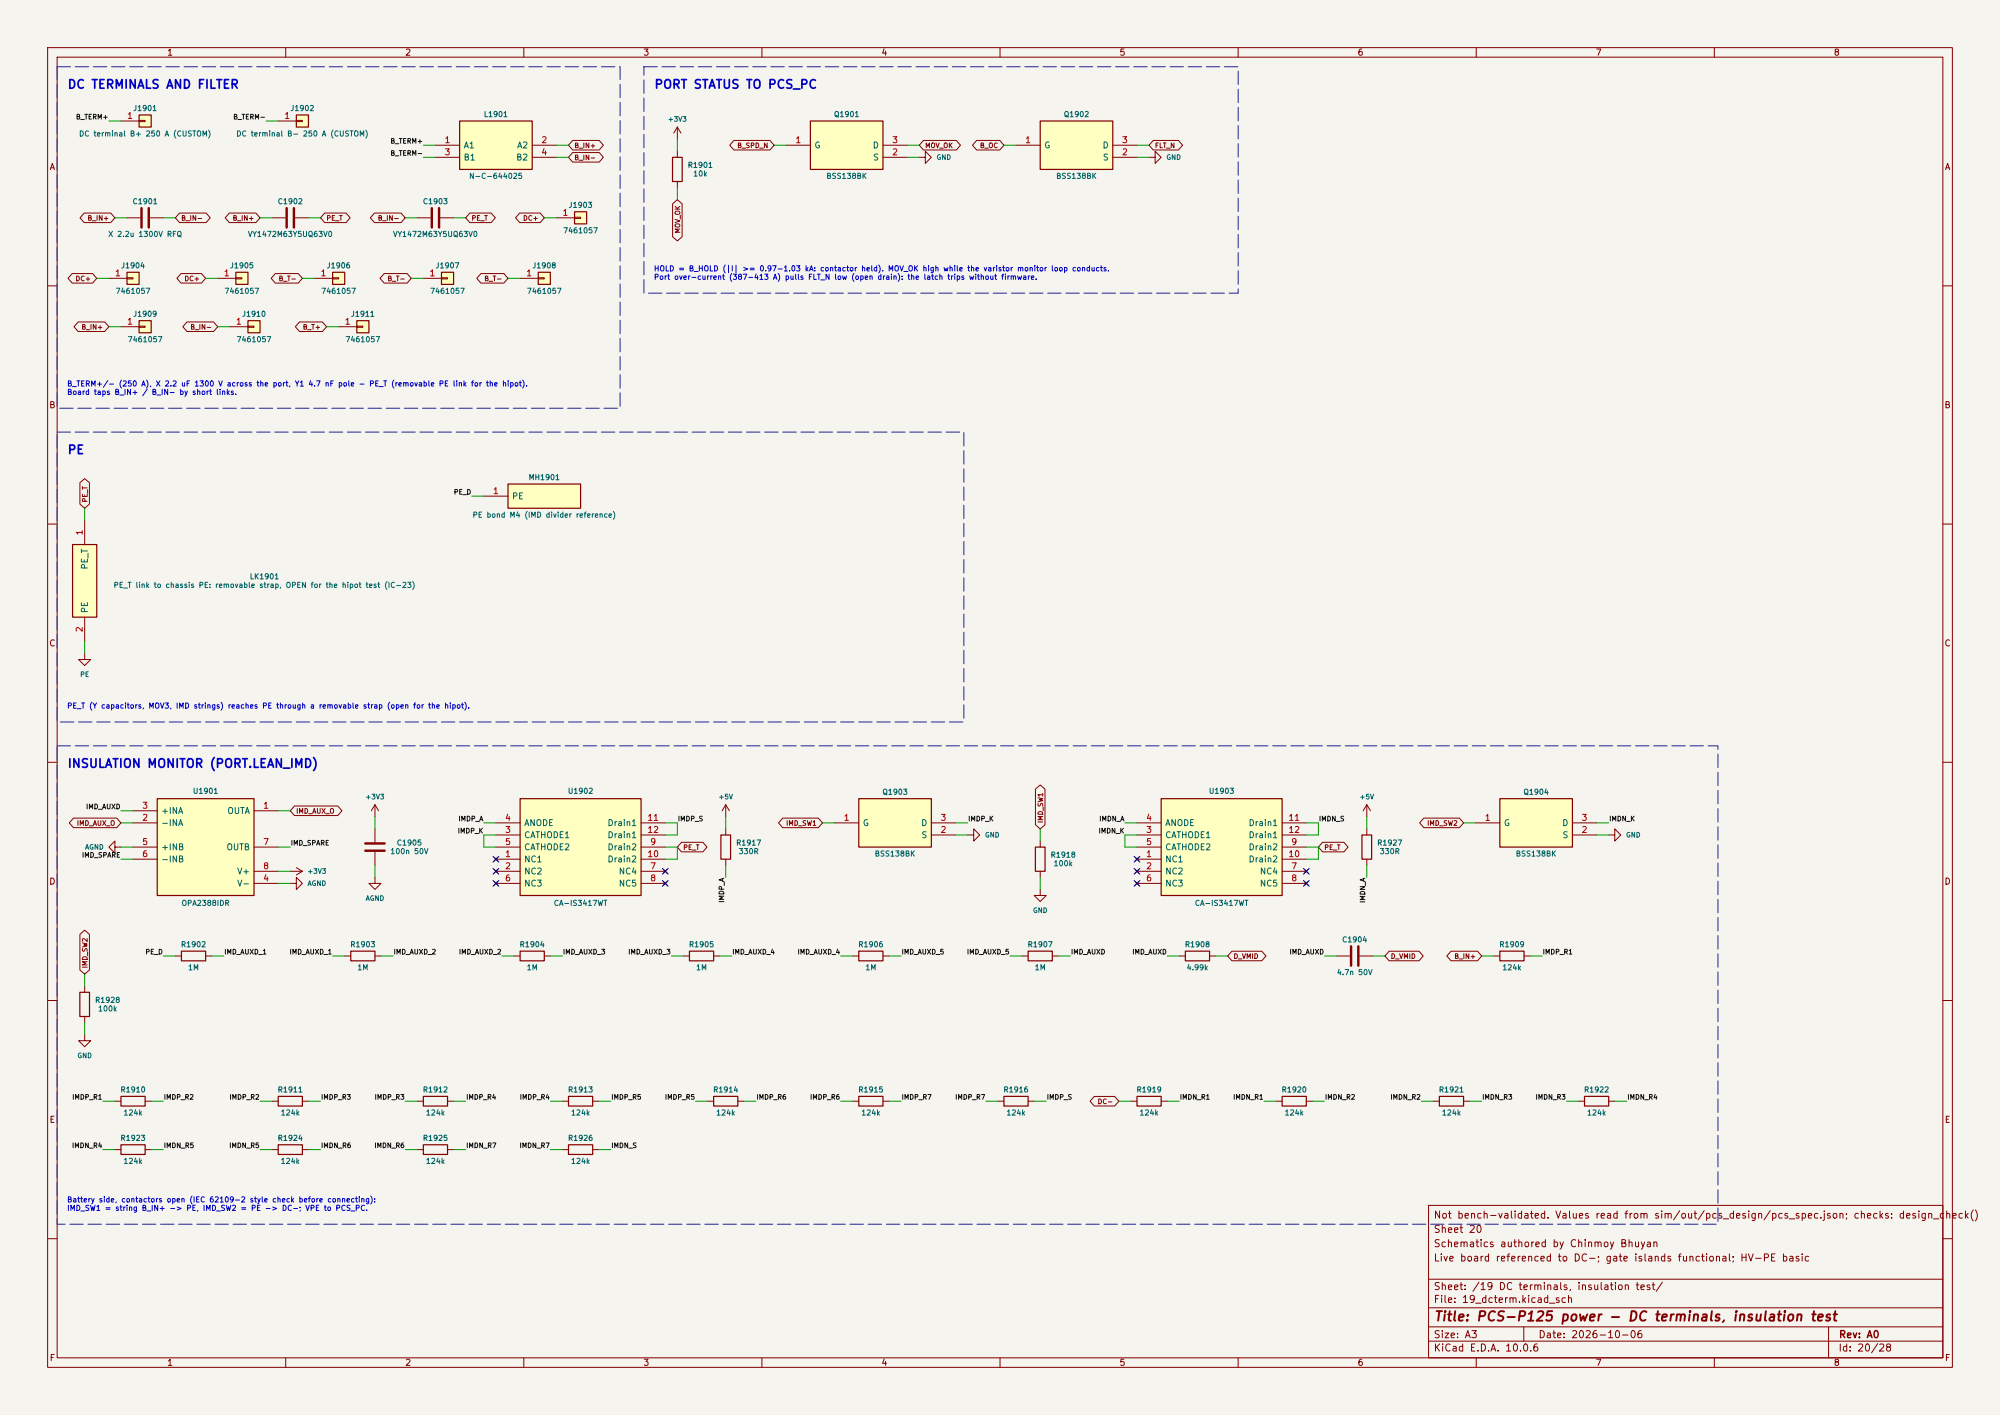
[picture p145: page 20]

PE_T (Y capacitors, MOV3, IMD strings) reaches PE through a removable strap (open for the hipot).

Battery side, contactors open (IEC 62109-2 style check before connecting):
IMD_SW1 = string B_IN+ -> PE, IMD_SW2 = PE -> DC-; VPE to PCS_PC.

Not bench-validated. Values read from sim/out/pcs_design/pcs_spec.json; checks: design_check()
Sheet 20
Schematics authored by Chinmoy Bhuyan
Live board referenced to DC-; gate islands functional; HV-PE basic

Sheet: /19 DC terminals, insulation test/
File: 19_dcterm.kicad_sch
Title: PCS-P125 power - DC terminals, insulation test

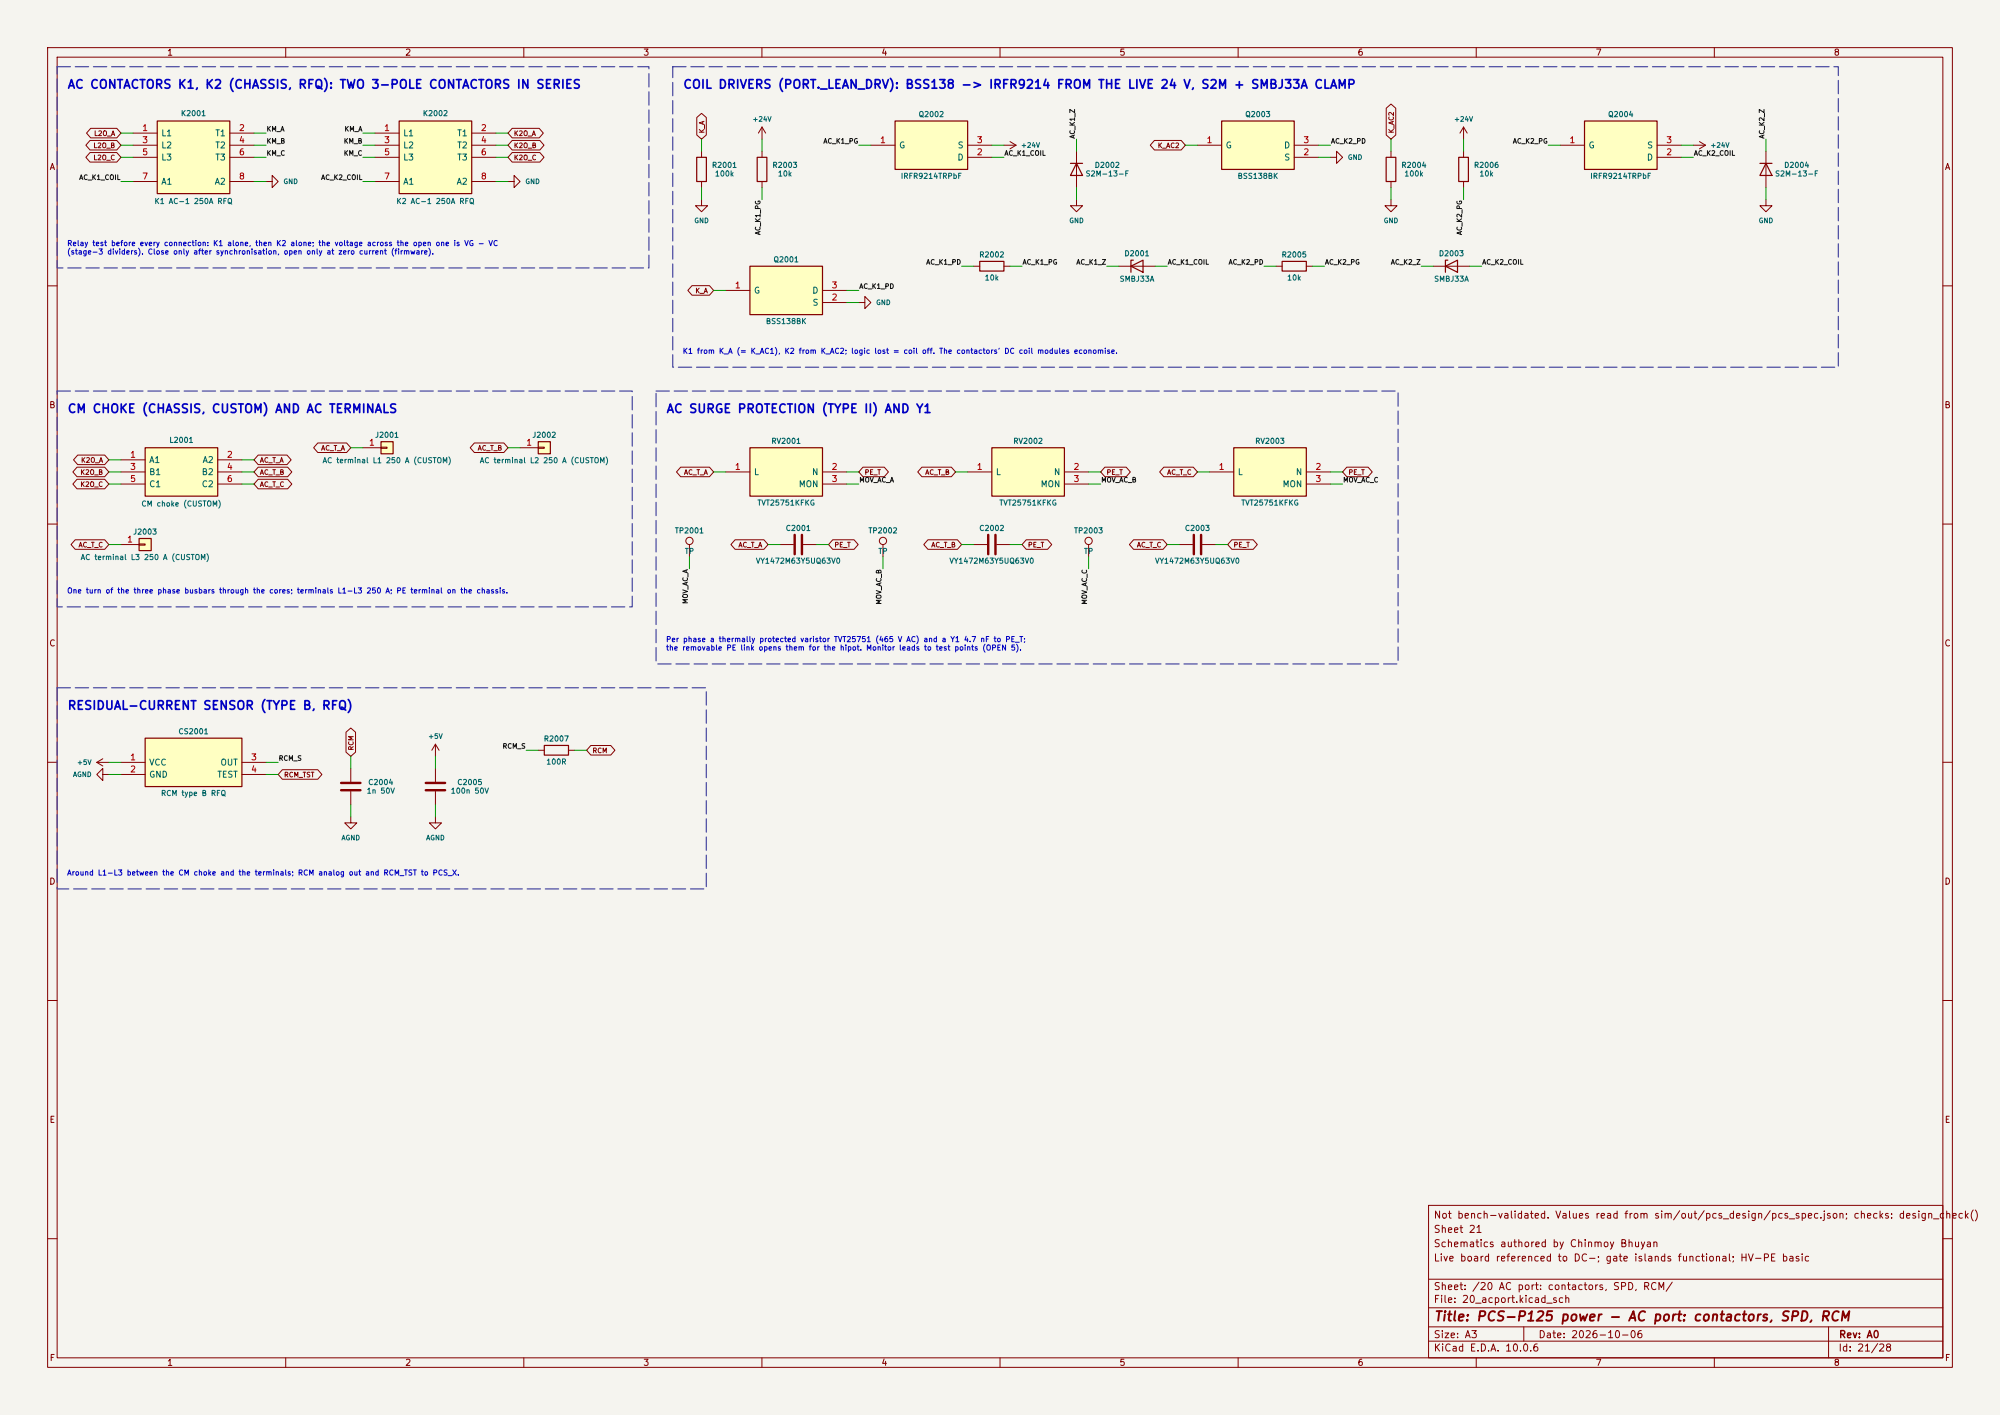
[picture p146: page 21]

AC CONTACTORS K1, K2 (CHASSIS, RFQ): TWO 3-POLE CONTACTORS IN SERIES

AC_K2_Z COIL DRIVERS (PORT._LEAN_DRV): BSS138 -> IRFR9214 FROM THE LIVE 24 V, S2M + SMBJ33A CLAMP

Relay test before every connection: K1 alone, then K2 alone; the voltage across the open one is VG - VC
(stage-3 dividers). Close only after synchronisation, open only at zero current (firmware).

K1 from K_A (= K_AC1), K2 from K_AC2; logic lost = coil off. The contactors' DC coil modules economise.

CM CHOKE (CHASSIS, CUSTOM) AND AC TERMINALS

RESIDUAL-CURRENT SENSOR (TYPE B, RFQ)

Not bench-validated. Values read from sim/out/pcs_design/pcs_spec.json; checks: design_check()
Sheet 21
Schematics authored by Chinmoy Bhuyan
Live board referenced to DC-; gate islands functional; HV-PE basic

Sheet: /20 AC port: contactors, SPD, RCM/
File: 20_acport.kicad_sch
Title: PCS-P125 power - AC port: contactors, SPD, RCM

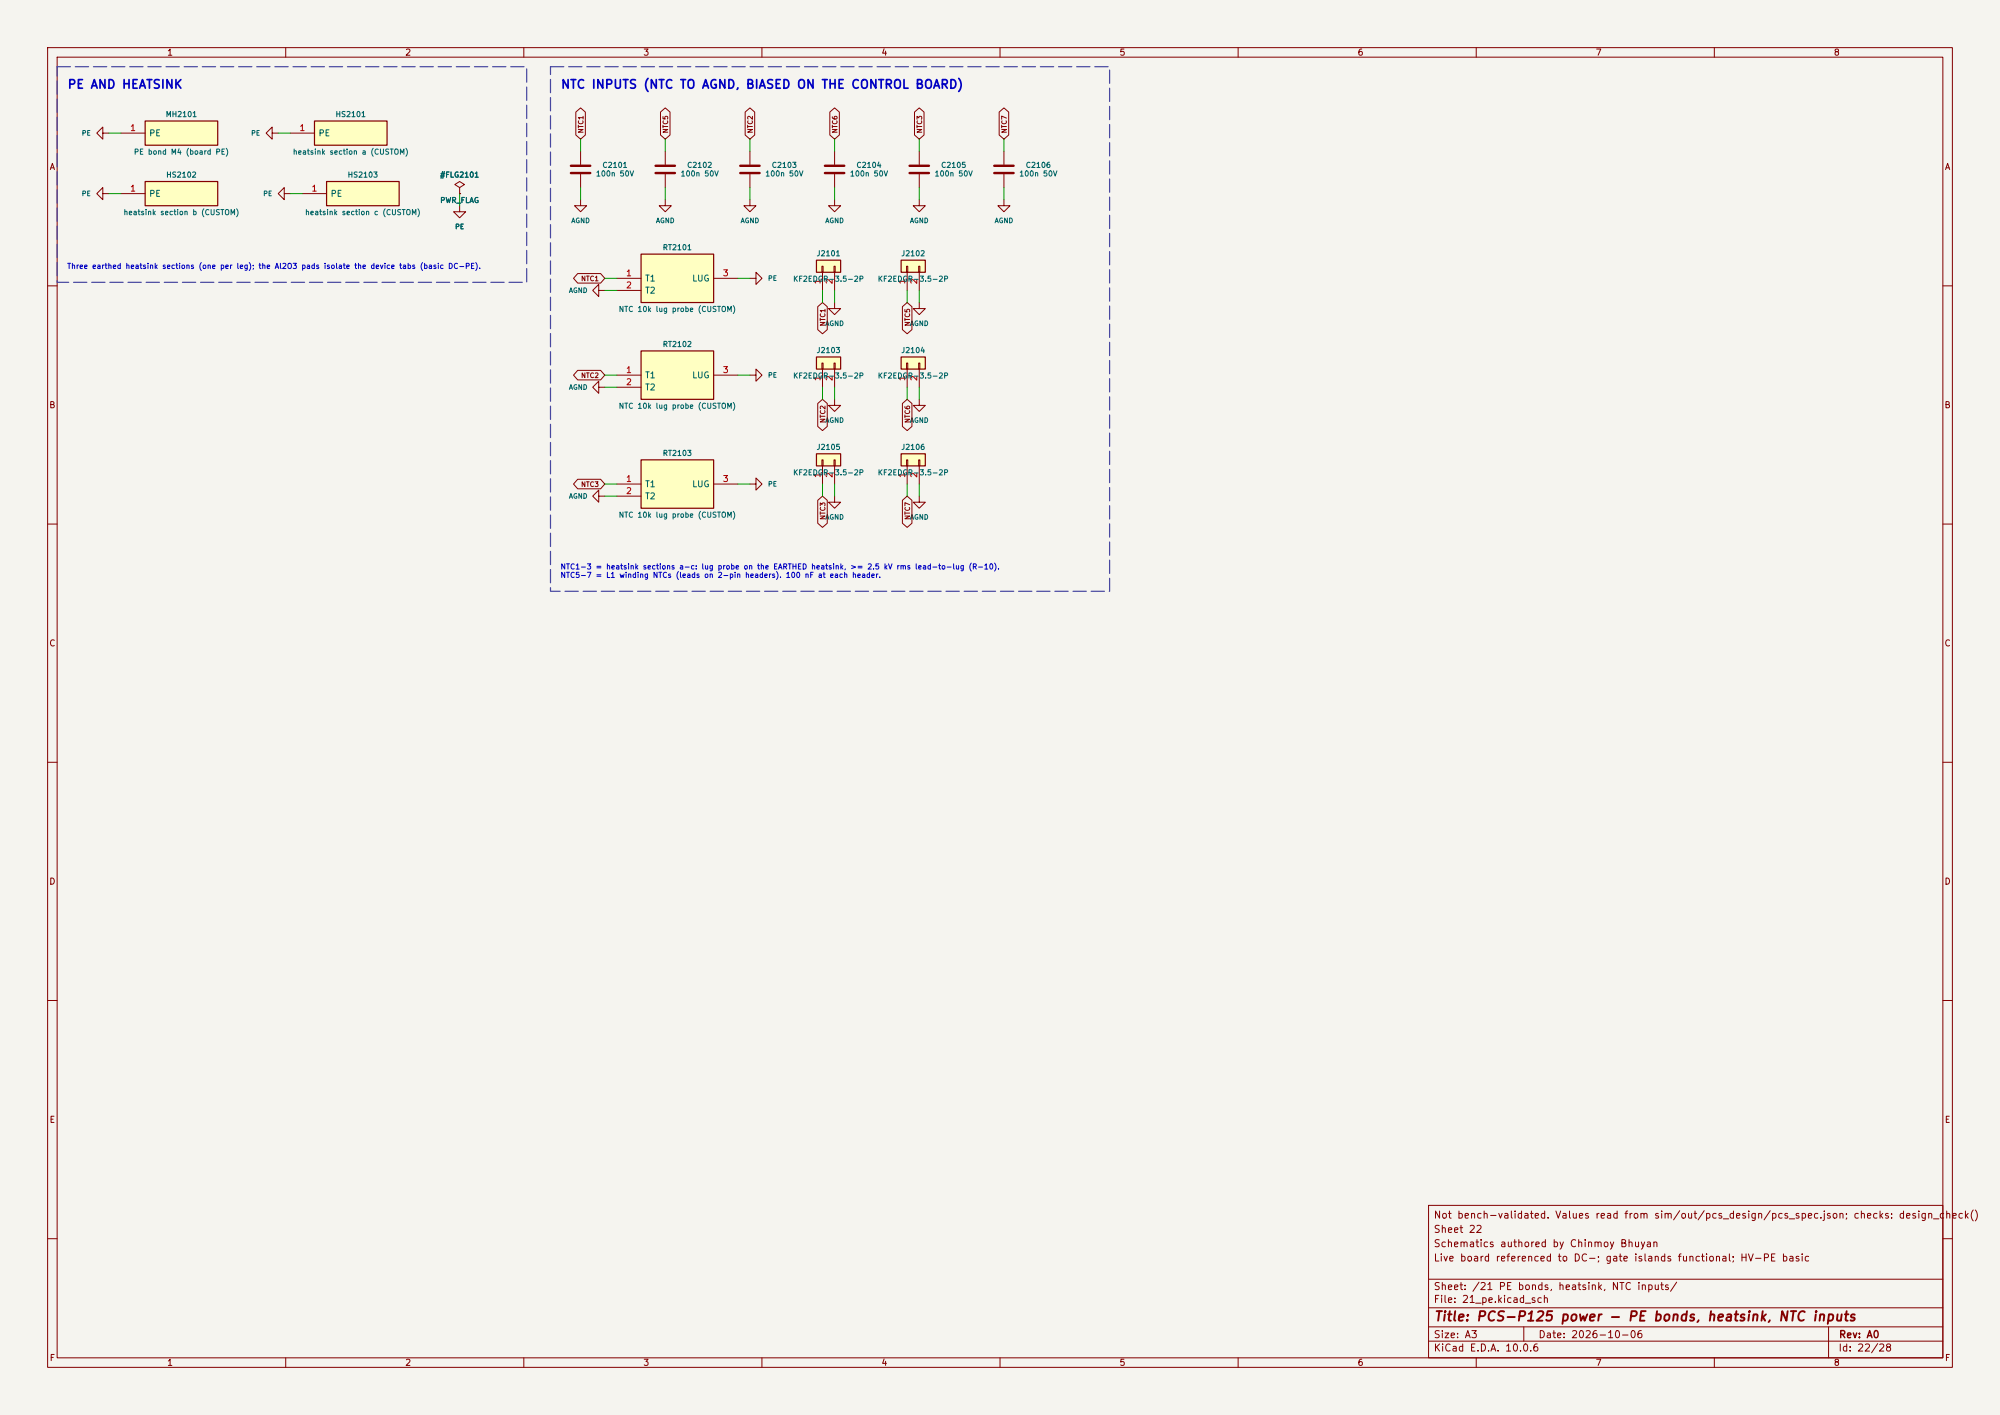
[picture p147: page 22]

RT2101 NTC 10k lug probe (CUSTOM) T1 1

heatsink section b (CUSTOM) PE

heatsink section a (CUSTOM) PE 1

Three earthed heatsink sections (one per leg); the Al2O3 pads isolate the device tabs (basic DC-PE).

NTC1-3 = heatsink sections a-c: lug probe on the EARTHED heatsink, >= 2.5 kV rms lead-to-lug (R-10). NTC5-7 = L1 winding NTCs (leads on 2-pin headers). 100 nF at each header.

Not bench-validated. Values read from sim/out/pcs_design/pcs_spec.json; checks: design_check()
Sheet 22
Schematics authored by Chinmoy Bhuyan
Live board referenced to DC-; gate islands functional; HV-PE basic

Sheet: /21 PE bonds, heatsink, NTC inputs/
File: 21_pe.kicad_sch
Title: PCS-P125 power - PE bonds, heatsink, NTC inputs

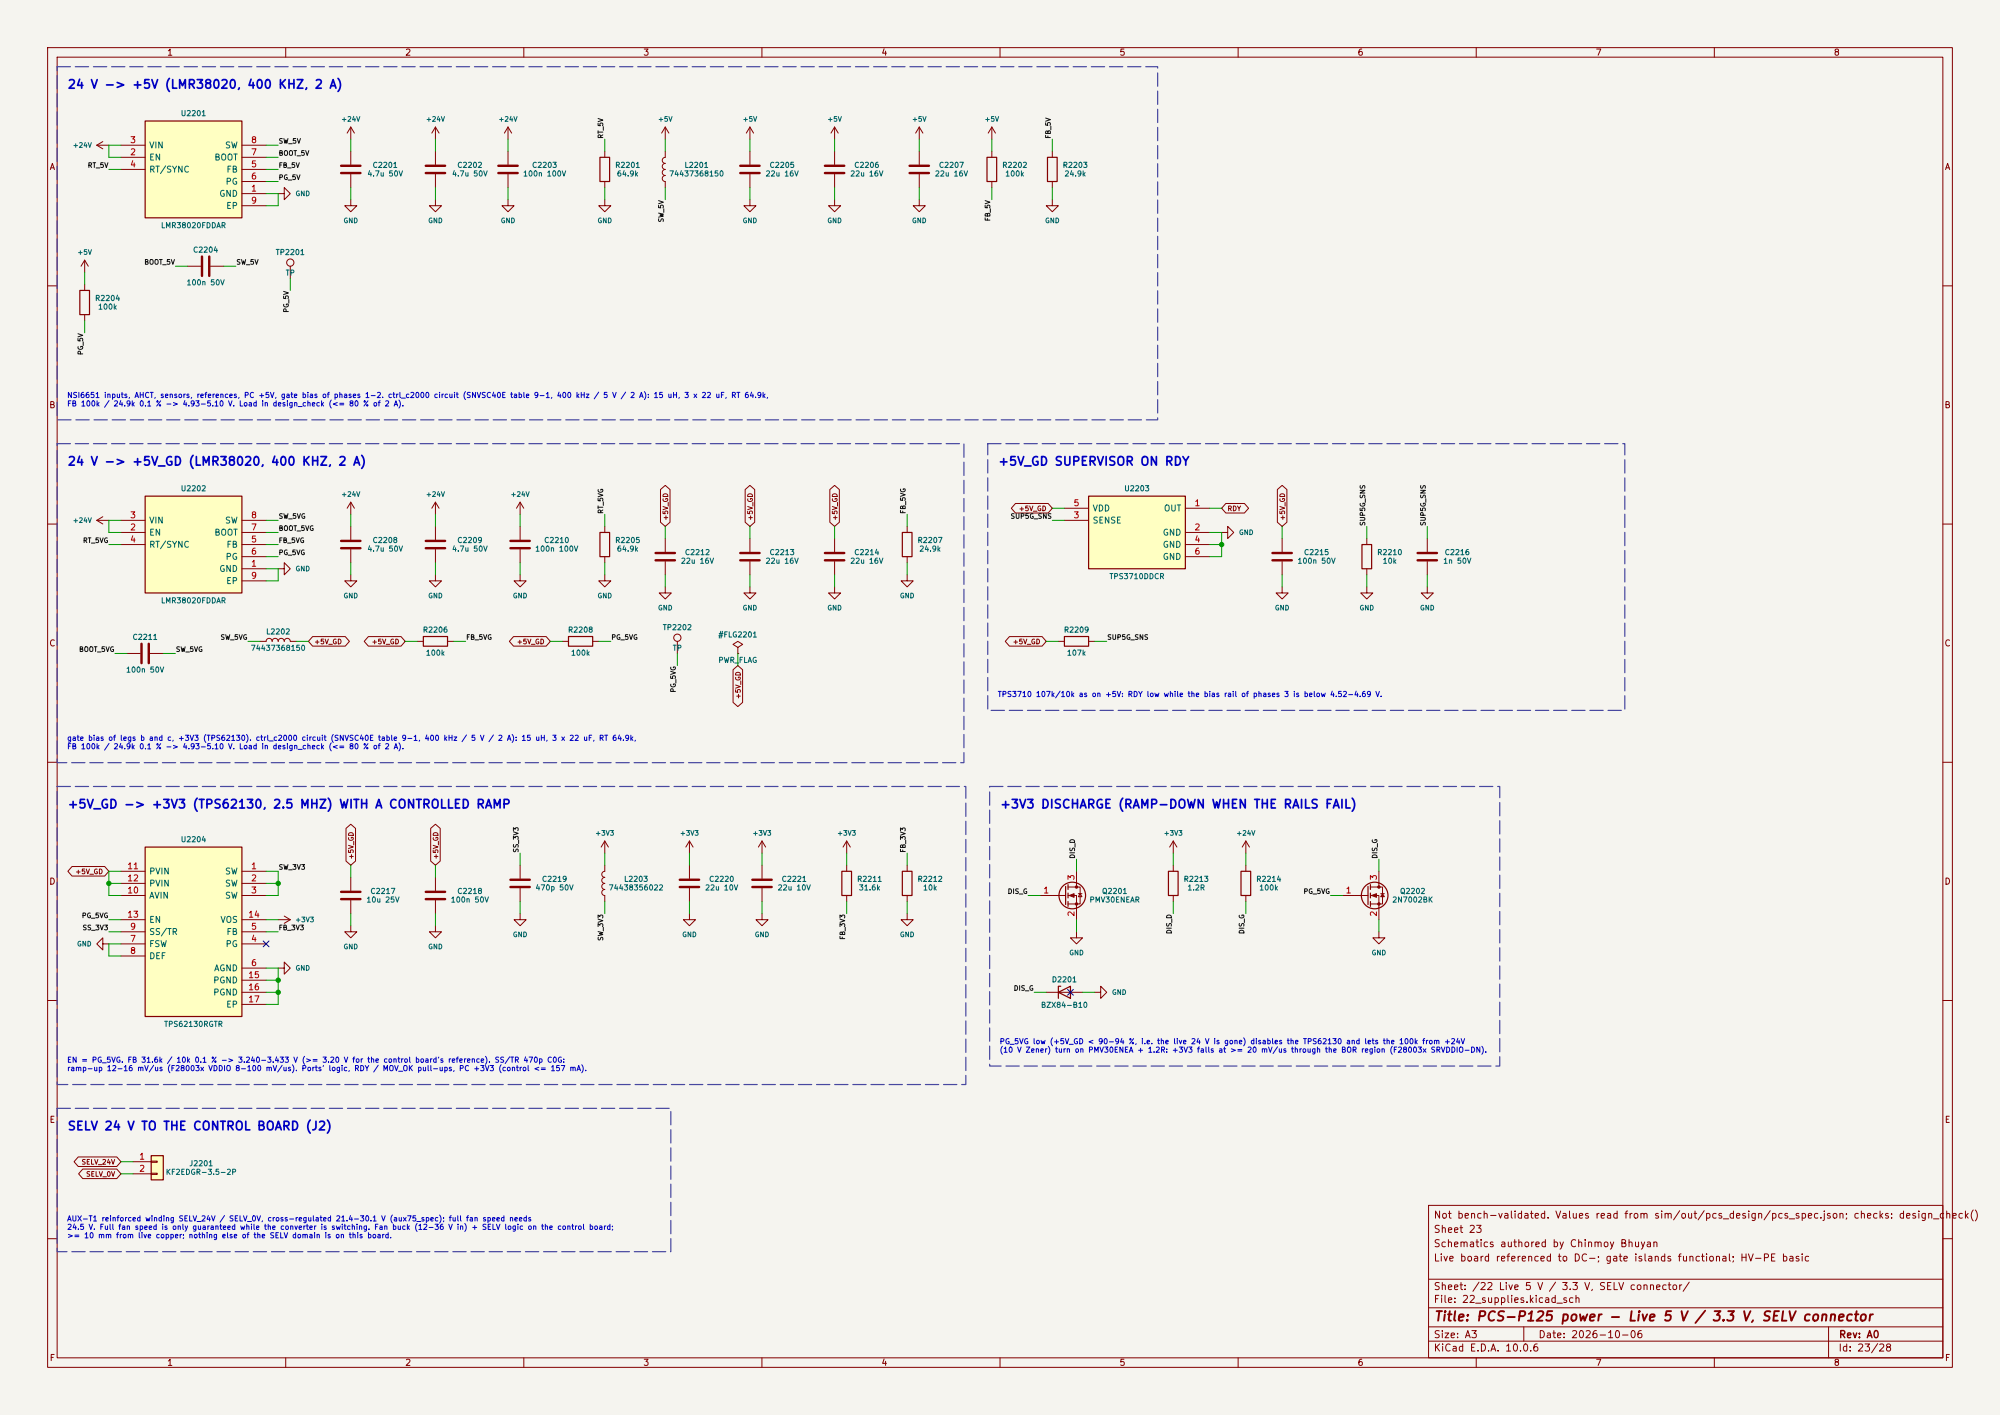
[picture p148: page 23]

NSI6651 inputs, AHCT, sensors, references, PC +5V, gate bias of phases 1-2. ctrl_c2000 circuit (SNVSC40E table 9-1, 400 kHz / 5 V / 2 A): 15 uH, 3 x 22 uF, RT 64.9k, FB 100k / 24.9k 0.1 % -> 4.93-5.10 V. Load in design_check (<= 80 % of 2 A).

(10 V Zener) turn on PMV30ENEA + 1.2R: +3V3 falls at >= 20 mV/us through the BOR region (F28003x SRVDDIO-DN).

EN = PG_5VG. FB 31.6k / 10k 0.1 % -> 3.240-3.433 V (>= 3.20 V for the control board's reference). SS/TR 470p C0G: ramp-up 12-16 mV/us (F28003x VDDIO 8-100 mV/us). Ports' logic, RDY / MOV_OK pull-ups, PC +3V3 (control <= 157 mA).

AUX-T1 reinforced winding SELV_24V / SELV_0V, cross-regulated 21.4-30.1 V (aux75_spec); full fan speed needs 24.5 V. Full fan speed is only guaranteed while the converter is switching. Fan buck (12-36 V in) + SELV logic on the control board; >= 10 mm from live copper; nothing else of the SELV domain is on this board. SELV 24 V TO THE CONTROL BOARD (J2)

Sheet 23
Schematics authored by Chinmoy Bhuyan
Live board referenced to DC-; gate islands functional; HV-PE basic

Sheet: /22 Live 5 V / 3.3 V, SELV connector/
File: 22_supplies.kicad_sch
Title: PCS-P125 power - Live 5 V / 3.3 V, SELV connector
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
