vectivolt/PCM/hardware/PORT-LEAN/outputs/PORT-LEAN_schematic.pdf

1 | 2 | 3 | 4 | 5 | 6 | 7 | 8

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
Size: A3 | Rev: F0 | F Date: 2026-10-04
KiCad E.D.A. 10.0.6 | Id: 1/9

# Title: Lean port sheets - Cover / Hierarchy

## File: PORT-LEAN.kicad_sch

## Sheet: /

## Live side referenced to BUS-; basic HV-PE; functional inside the live side

## Schematics authored by Chinmoy Bhuyan

## Sheet 1

## Not bench-validated. Values: sim/port_design.py -> port_spec.json 'lean'

# 08 Insulation monitor

File: sheets/08_lean_imd.kicad_sch 07 Port B coil drives

File: sheets/07_leanB_drive.kicad_sch 03 Port A sensing and interlocks

File: sheets/03_leanA_ctrl.kicad_sch | 04 Port A coil drives

File: sheets/04_leanA_drive.kicad_sch 02 Port A power path (pv)

File: sheets/02_leanA_power.kicad_sch

# 01 Supplies and commands

File: sheets/01_lean_io.kicad_sch 05 Port B power path (battery)

File: sheets/05_leanB_power.kicad_sch

# 06 Port B sensing and interlocks

File: sheets/06_leanB_ctrl.kicad_sch | Contactor + precharge relay: interlock logic, fail-safe high side, economiser; | PE divider, two switched 992 k strings through CA-IS3417WT passive bank bleeder | Contactor: interlock logic, fail-safe high side, economiser;

passive bank bleeder References, BUS- shunt amplifier + hold-off / OC windows, dividers, dV amplifier, polarity and dV interlocks Rev F0 | 2026-10-04 | Schematics authored by Chinmoy Bhuyan | D-044 lean ports A (PV) and B (battery) + insulation monitor, BUS- referenced

Live 24 V / 5 V / 3.3 V, BUS- tie, commands | Varistor Y + monitor Lean port sheets

Varistor Y + monitor, aR fuses Verification build of the reusable lean-port functions of gen/port.py (lean_port, varistor_y, lean_contactor, lean_precharge, lean_bleeder, lean_dividers, lean_shunt, lean_interlock, lean_imd). The product sheets live on the power board.

References, BUS- shunt amplifier + hold-off / OC windows, dividers, dV amplifier,

### polarity and dV interlocks

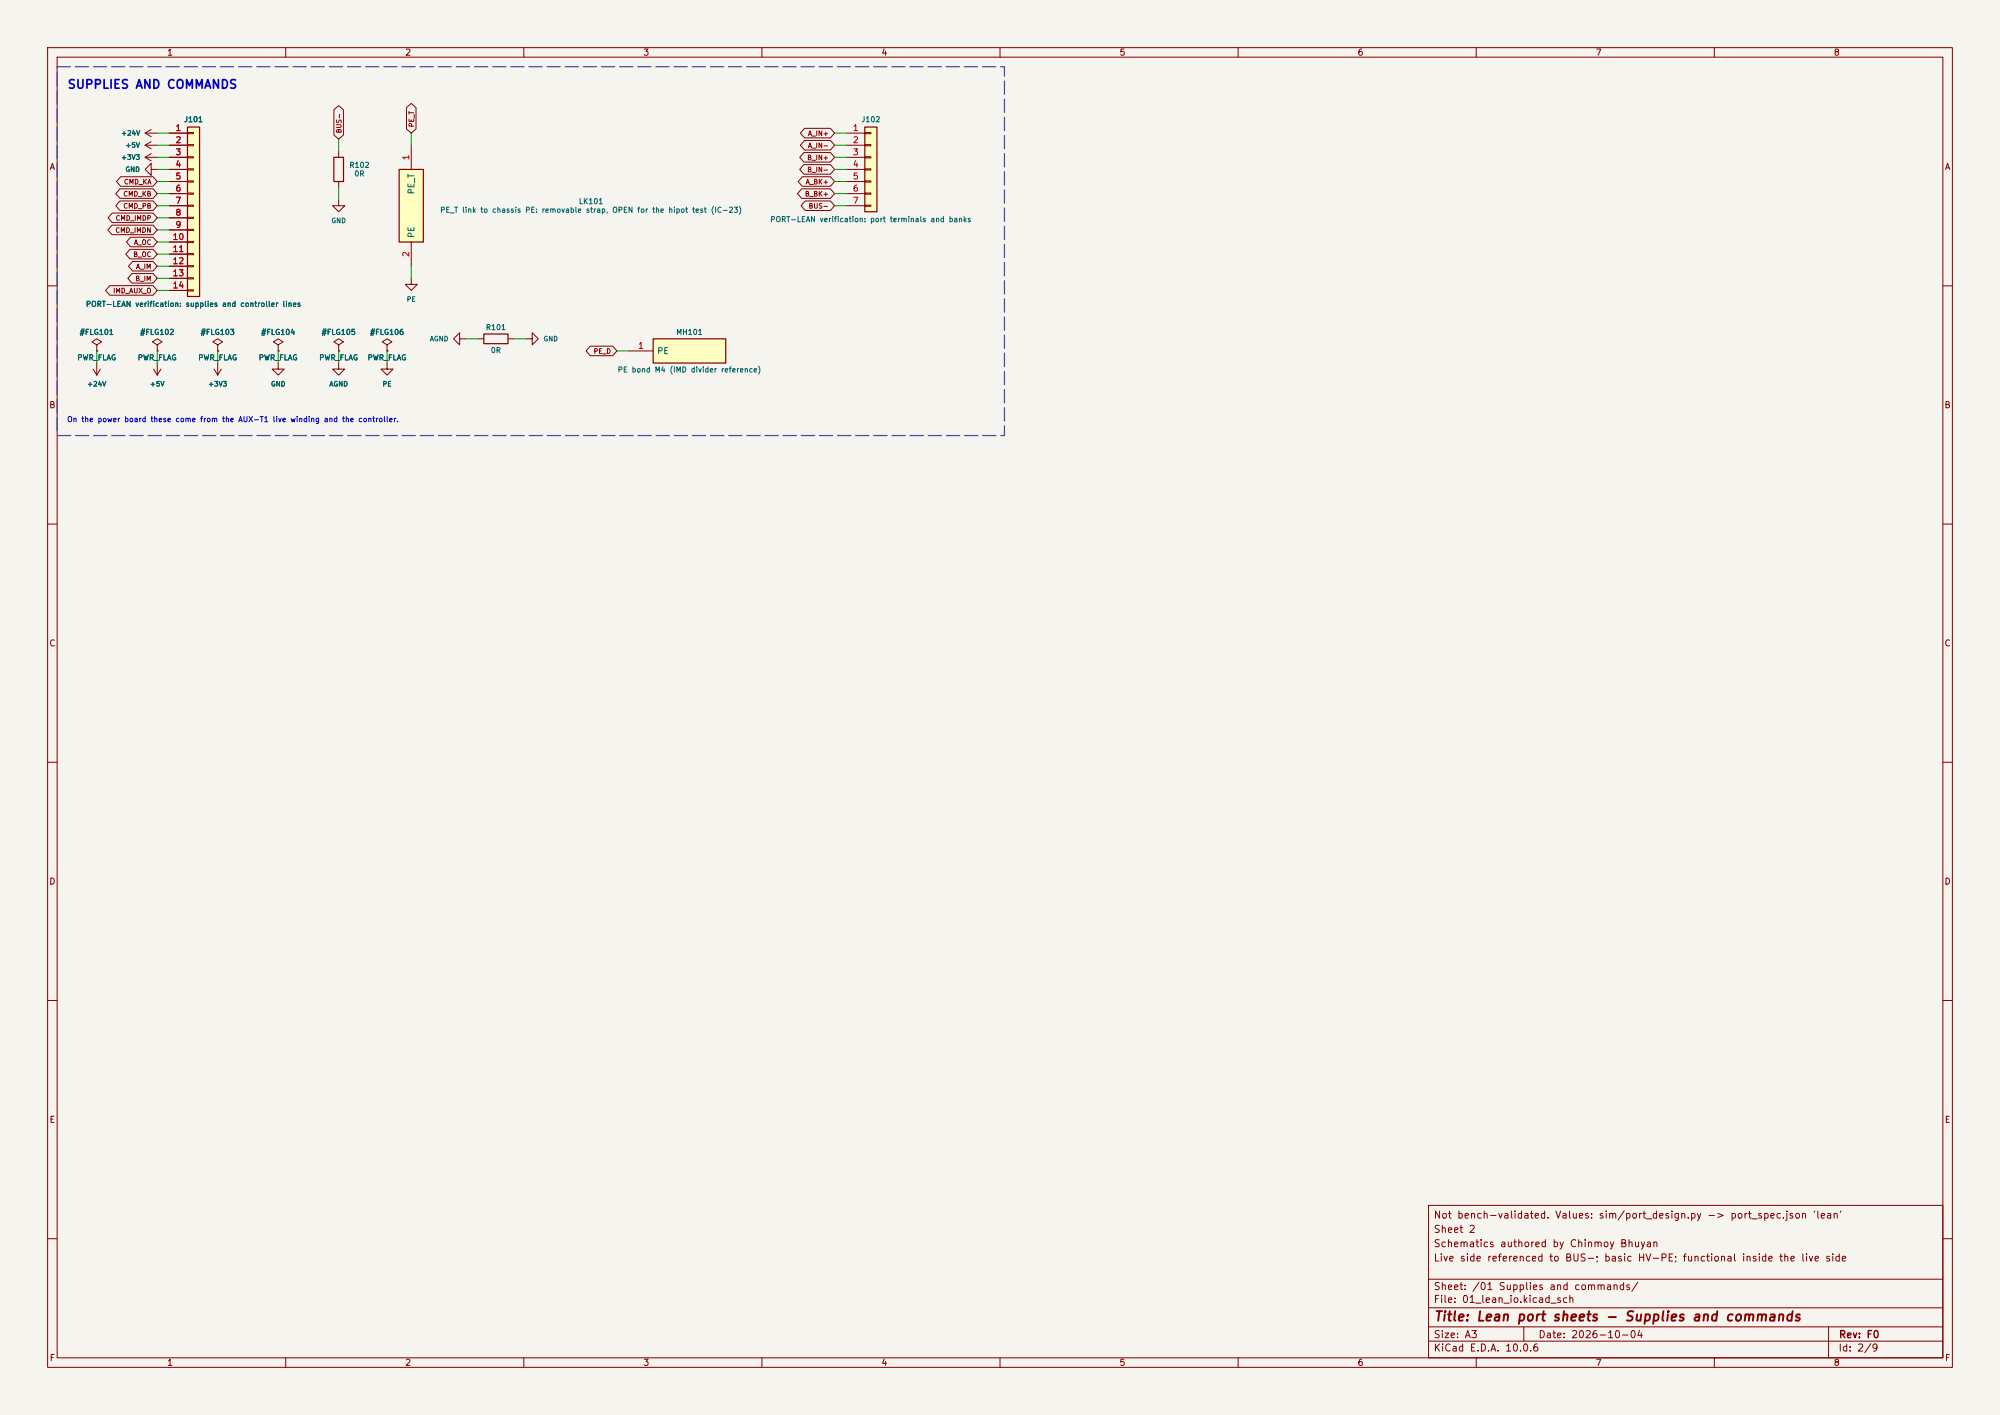
[picture p157: page 2]

J101 PORT-LEAN verification: supplies and controller lines 1

J102 PORT-LEAN verification: port terminals and banks PE_T 1 PE 2

Not bench-validated. Values: sim/port_design.py -> port_spec.json 'lean'
Sheet 2
Schematics authored by Chinmoy Bhuyan
Live side referenced to BUS-; basic HV-PE; functional inside the live side

Sheet: /01 Supplies and commands/
File: 01_lean_io.kicad_sch
Title: Lean port sheets - Supplies and commands

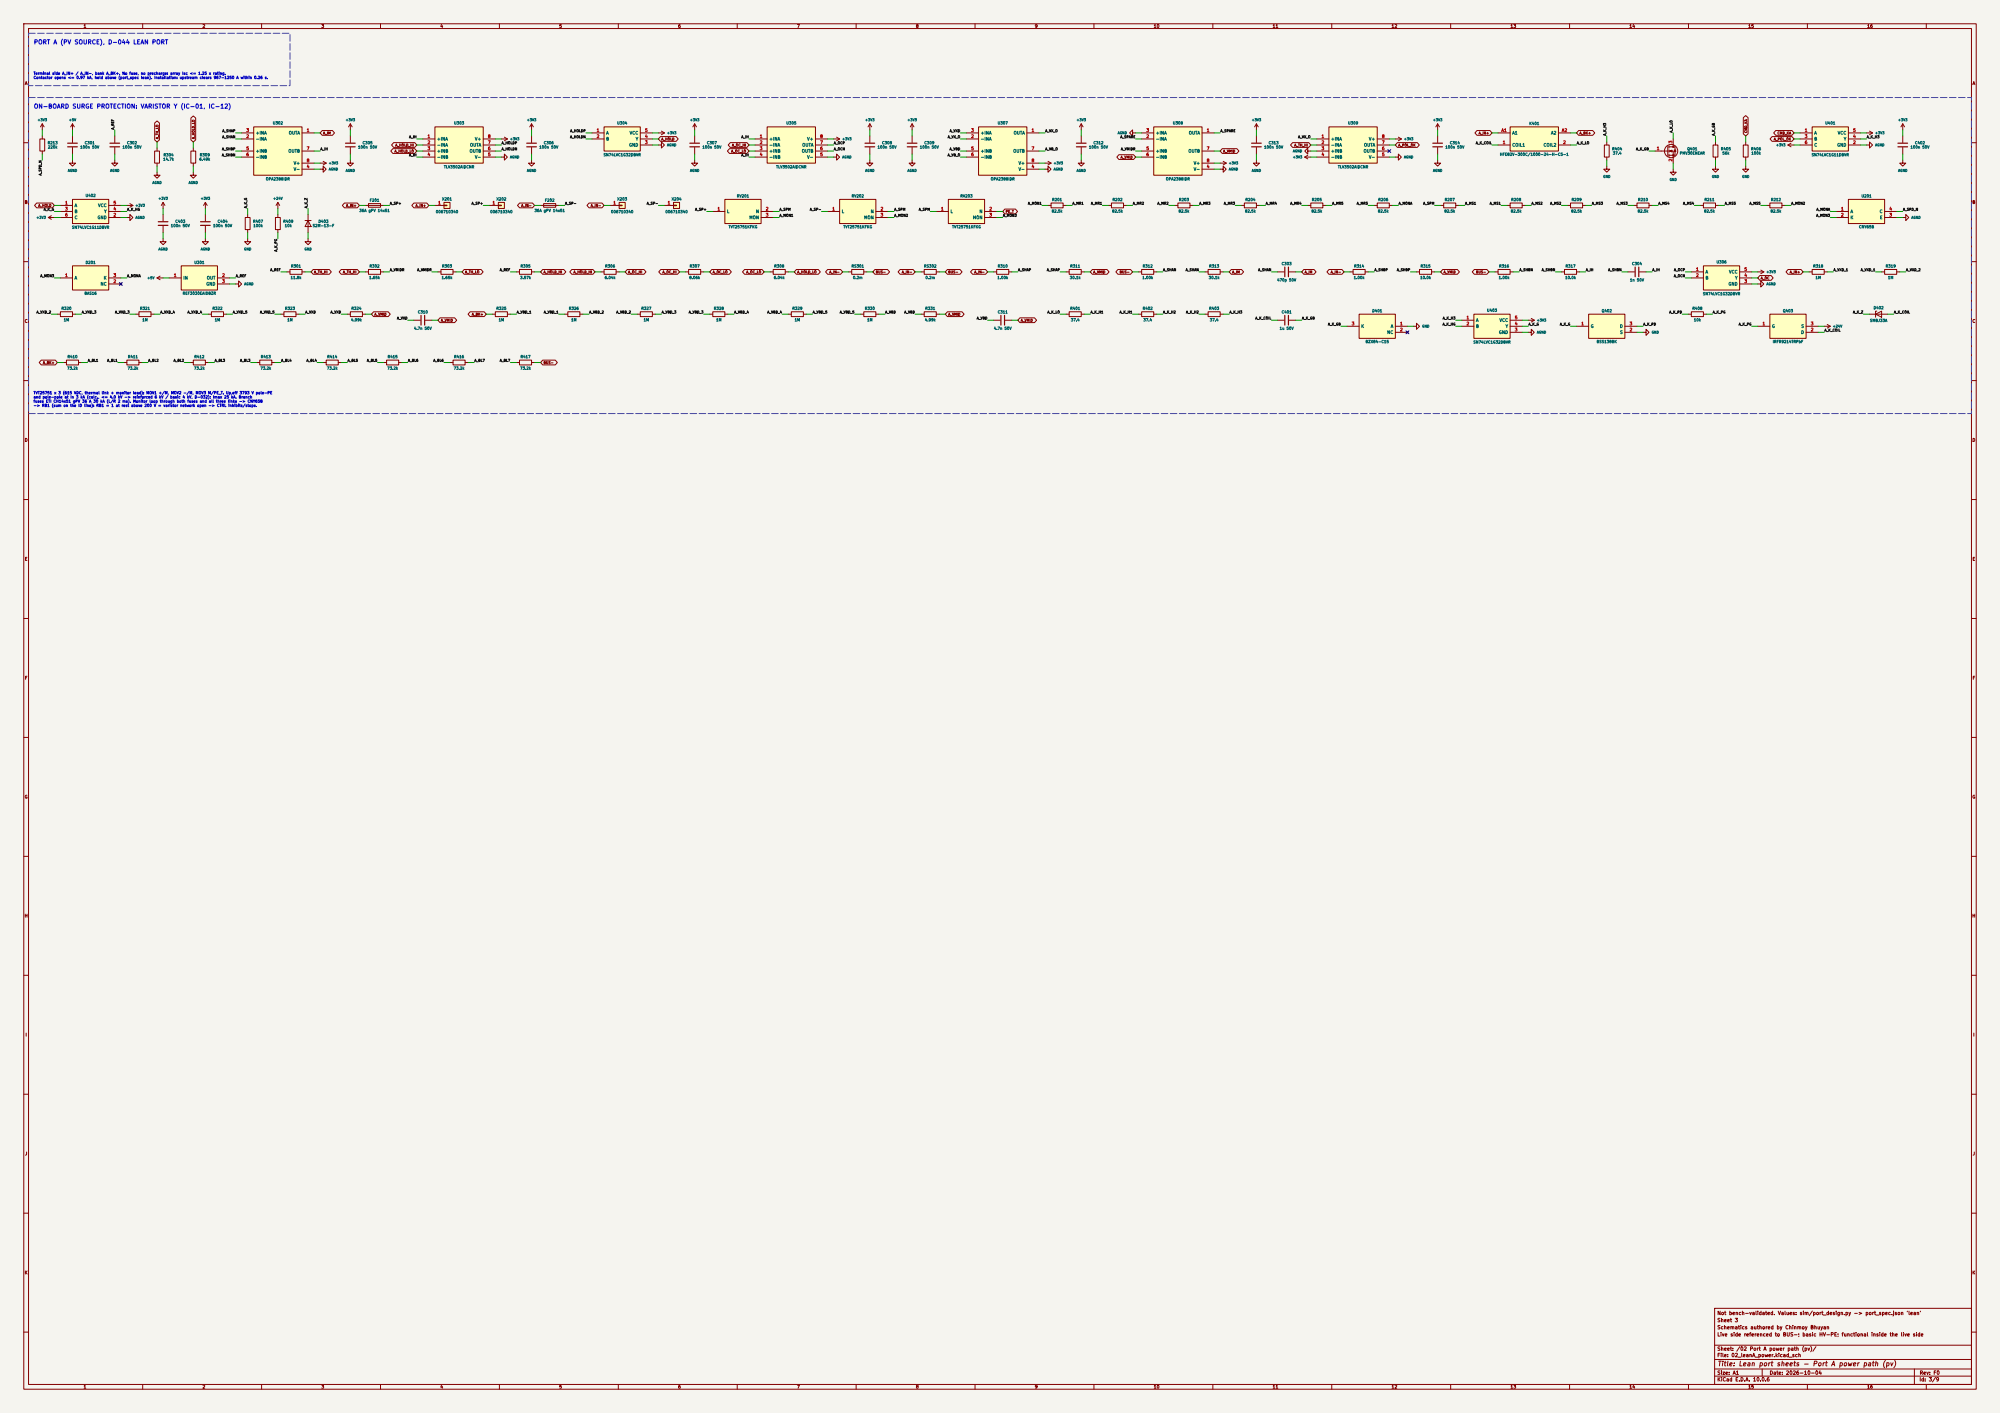
[picture p158: page 3]

Terminal side A_IN+ / A_IN-, bank A_BK+. No fuse, no precharge: array Isc <= 1.25 x rating. Contactor opens <= 0.97 kA, held above (port_spec lean). Installation: upstream clears 967-1250 A within 0.26 s. PORT A (PV SOURCE), D-044 LEAN PORT

ON-BOARD SURGE PROTECTION: VARISTOR Y (IC-01, IC-12)

TVT25751 x 3 (615 VDC, thermal link + monitor lead): MOV1 +/M, MOV2 -/M, MOV3 M/PE_T. Up,eff 3793 V pole-PE
and pole-pole at In 3 kA (calc., <= 4.0 kV -> reinforced 6 kV / basic 4 kV, D-032); Imax 25 kA. Branch
fuses ETI CH14x51 gPV 36 A 30 kA (L/R 2 ms). Monitor loop through both fuses and all three links -> CNY65B -> RB1 (sum on the ID line): RB1 = 1 at rest above 200 V = varistor network open -> CTRL inhibits/stops.

Not bench-validated. Values: sim/port_design.py -> port_spec.json 'lean'
Sheet 3
Schematics authored by Chinmoy Bhuyan
Live side referenced to BUS-; basic HV-PE; functional inside the live side

Sheet: /02 Port A power path (pv)/
File: 02_leanA_power.kicad_sch
Title: Lean port sheets - Port A power path (pv)


Not bench-validated. Values: sim/port_design.py -> port_spec.json 'lean'
Sheet 4
Schematics authored by Chinmoy Bhuyan
Live side referenced to BUS-; basic HV-PE; functional inside the live side

Sheet: /03 Port A sensing and interlocks/
File: 03_leanA_ctrl.kicad_sch
Title: Lean port sheets - Port A sensing and interlocks


Not bench-validated. Values: sim/port_design.py -> port_spec.json 'lean'
Sheet 5
Schematics authored by Chinmoy Bhuyan
Live side referenced to BUS-; basic HV-PE; functional inside the live side

Sheet: /04 Port A coil drives/
File: 04_leanA_drive.kicad_sch
Title: Lean port sheets - Port A coil drives

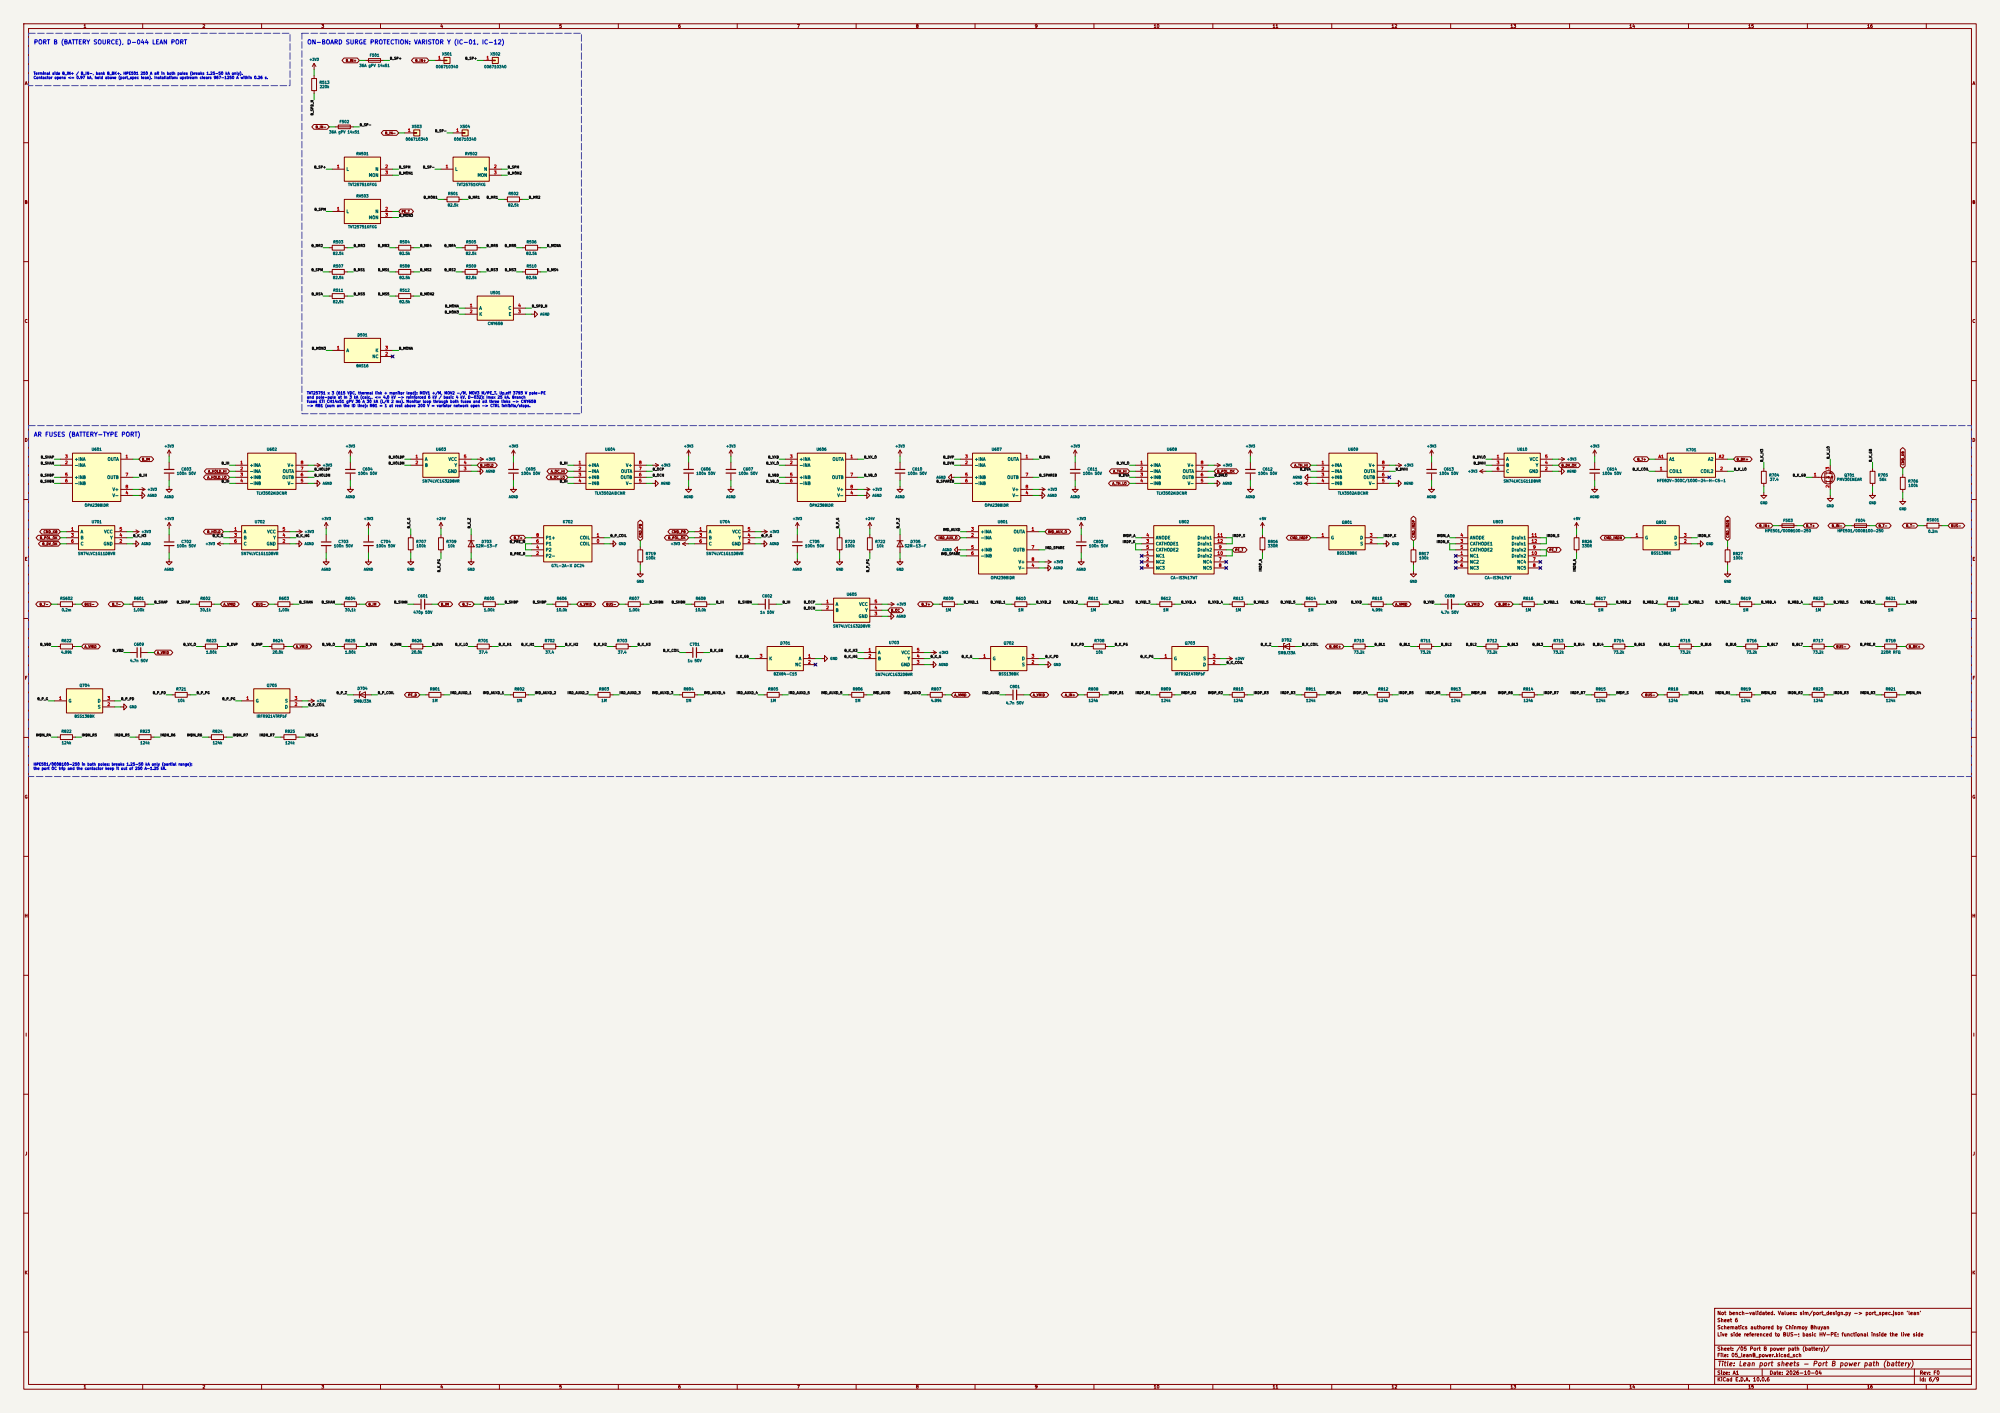
[picture p159: page 6]

Terminal side B_IN+ / B_IN-, bank B_BK+. HPE501 250 A aR in both poles (breaks 1.25-50 kA only). Contactor opens <= 0.97 kA, held above (port_spec lean). Installation: upstream clears 967-1250 A within 0.26 s. PORT B (BATTERY SOURCE), D-044 LEAN PORT

ON-BOARD SURGE PROTECTION: VARISTOR Y (IC-01, IC-12)

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

Not bench-validated. Values: sim/port_design.py -> port_spec.json 'lean'
Sheet 6
Schematics authored by Chinmoy Bhuyan
Live side referenced to BUS-; basic HV-PE; functional inside the live side

Sheet: /05 Port B power path (battery)/
File: 05_leanB_power.kicad_sch
Title: Lean port sheets - Port B power path (battery)


Not bench-validated. Values: sim/port_design.py -> port_spec.json 'lean'
Sheet 7
Schematics authored by Chinmoy Bhuyan
Live side referenced to BUS-; basic HV-PE; functional inside the live side

Sheet: /06 Port B sensing and interlocks/
File: 06_leanB_ctrl.kicad_sch
Title: Lean port sheets - Port B sensing and interlocks


Not bench-validated. Values: sim/port_design.py -> port_spec.json 'lean'
Sheet 8
Schematics authored by Chinmoy Bhuyan
Live side referenced to BUS-; basic HV-PE; functional inside the live side

Sheet: /07 Port B coil drives/
File: 07_leanB_drive.kicad_sch
Title: Lean port sheets - Port B coil drives


Not bench-validated. Values: sim/port_design.py -> port_spec.json 'lean'
Sheet 9
Schematics authored by Chinmoy Bhuyan
Live side referenced to BUS-; basic HV-PE; functional inside the live side

Sheet: /08 Insulation monitor/
File: 08_lean_imd.kicad_sch
Title: Lean port sheets - Insulation monitor
