vectivolt/PCM/hardware/PV-CTL/outputs/PV-CTL_schematic.pdf

1 | 2 | 3 | 4 | 5 | 6 | 7 | 8

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
Size: A3 | Rev: A2
KiCad E.D.A. 10.0.6 | Id: 1/9 | F Date: 2026-10-06

# Title: PV-CTL control board - Cover / Hierarchy

## File: PV-CTL.kicad_sch

## Sheet: /

## LIVE zone = BUS- (hazardous live); SELV zone behind reinforced barrier B1

## Schematics authored by Chinmoy Bhuyan

## Sheet 1

Not bench-validated. All bands and budgets calculated in design_check().

# 08 Ethernet bridge (EMS, Modbus TCP)

# File: sheets/08_eth.kicad_sch 04 Hardware trip comparators

File: sheets/04_trip.kicad_sch

# 06 Barrier B1: isolators, CAN, RS-485

File: sheets/06_iso.kicad_sch 01 PC connector, supply, reset File: sheets/01_supply.kicad_sch

# 05 Trip latch, watchdog, gating

File: sheets/05_latch.kicad_sch | 07 SELV supply, fans, stop, DI1, relay

# File: sheets/07_selv.kicad_sch 02 F280039C, clock, debug, recorder flash

File: sheets/02_mcu.kicad_sch | 03 Reference and analog front ends
File: sheets/03_afe.kicad_sch | 7 x TLV9024 on +3V3 (open drain, no firmware): IL windows from each sensor's Uref; VA / VB over-voltage, NTC over-temperature and open probe from VREF ladders WCH CH9121T UART-to-Ethernet bridge on the SELV side, HR913550AE RJ45 with | magnetics,
SRV05-4, TPS7A2033 3.3 V. NOT FITTED on PV-CTL / PV-CTL-P75: footprints only (DNP). REF3030E 3.0 V = VREFHI = VDAC = NTC bias = trip thresholds; IL1-4 gain stages;

### power-board signals into the ADC through 100 R / 1 nF; 8 NTC biases + inlet NTC

SELV 24 V input (AUX-T1 reinforced winding, 12-36 V), TPS54360B 5 V and fan supply, 3 fan headers + tach, stop (chainable) / ready / DI1 terminals, relay, SELV 0 V to PE 74LVC07 wired-AND of every trip source -> PRE_N -> 74LVC1G74 latch (no firmware); heartbeat monoflop; 74LVC08 gating of 16 PWM, EN, K_A, K_B, K_PRE, STATUS, FAN

Assembly option: the Ethernet bridge (sheet 08_eth) is NOT FITTED on PV-CTL / PV-CTL-P75 (DNP); fitted on PCS-CTL. Debug header in cJTAG mode only. Pin plan: gen/data/pv_ctrl_pin_plan.csv (from SPRSP61C, checked every build).

Assembly option: the two TLV9024 marked 'PV-P100/110 only' are not fitted on PV-P75 (bom/PV-CTL-P75_BOM.csv).

2x32 PC contract to the power board (all LIVE): only +3V3 is used (200 mA allocated by PV-PWR); TPS3828 reset + 1.6 s watchdog

ARCHITECTURE-COSTFIRST sections 6.1 (trip sources -> one latch), 10 (two zones); PC levels as built on PV-PWR (hardware/PV-PWR/outputs/PV-PWR_design_check.txt).

### TMS320F280039C (100-pin PZ), decoupling, 25 MHz SPXO, cTI-20 header in cJTAG mode

(LIVE), 4 MB recorder flash, boot straps, command pull-downs

Rev A2 | 2026-10-06 | Schematics authored by Chinmoy Bhuyan | Cost-first PV-P75/100/110 controller: F280039C on BUS-, one trip latch, one SELV barrier

# PV-CTL control board

Reinforced barrier B1: CA-IS3050W CAN, CA-IS3082WNX RS-485, 2 x CA-IS3821LG,

### CA-IS3820LG, CA-IS3842HW (Ethernet UART, DI1); bus TVS, jumper terminations (SELV)

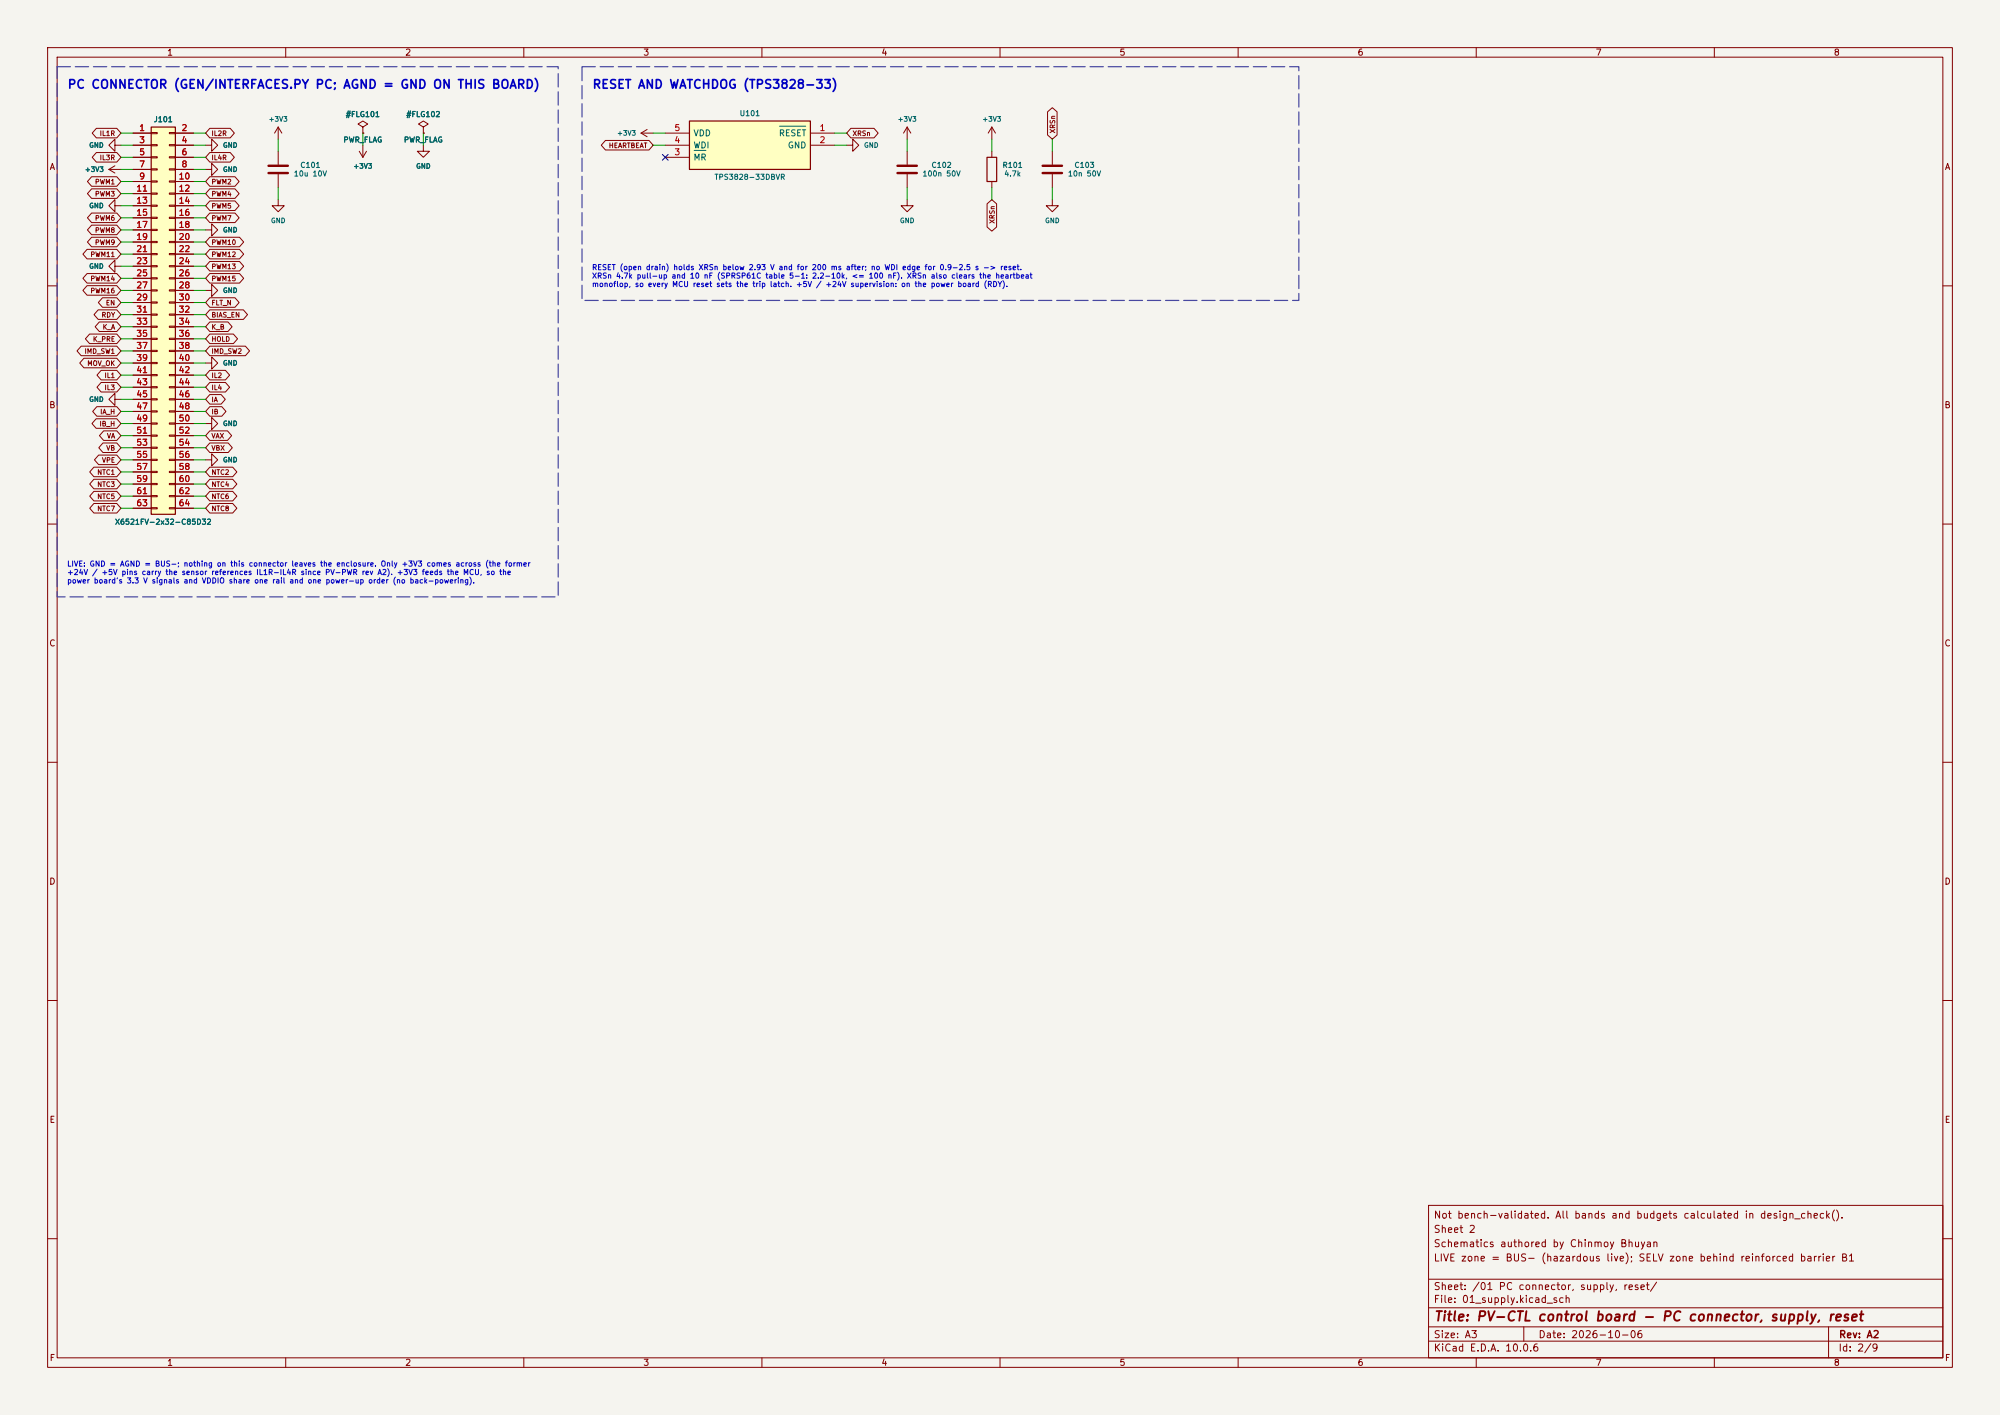
[picture p160: page 2]

PC CONNECTOR (GEN/INTERFACES.PY PC; AGND = GND ON THIS BOARD)

LIVE: GND = AGND = BUS-; nothing on this connector leaves the enclosure. Only +3V3 comes across (the former +24V / +5V pins carry the sensor references IL1R-IL4R since PV-PWR rev A2). +3V3 feeds the MCU, so the power board's 3.3 V signals and VDDIO share one rail and one power-up order (no back-powering).

Not bench-validated. All bands and budgets calculated in design_check().
Sheet 2
Schematics authored by Chinmoy Bhuyan
LIVE zone = BUS- (hazardous live); SELV zone behind reinforced barrier B1

Sheet: /01 PC connector, supply, reset/
File: 01_supply.kicad_sch
Title: PV-CTL control board - PC connector, supply, reset

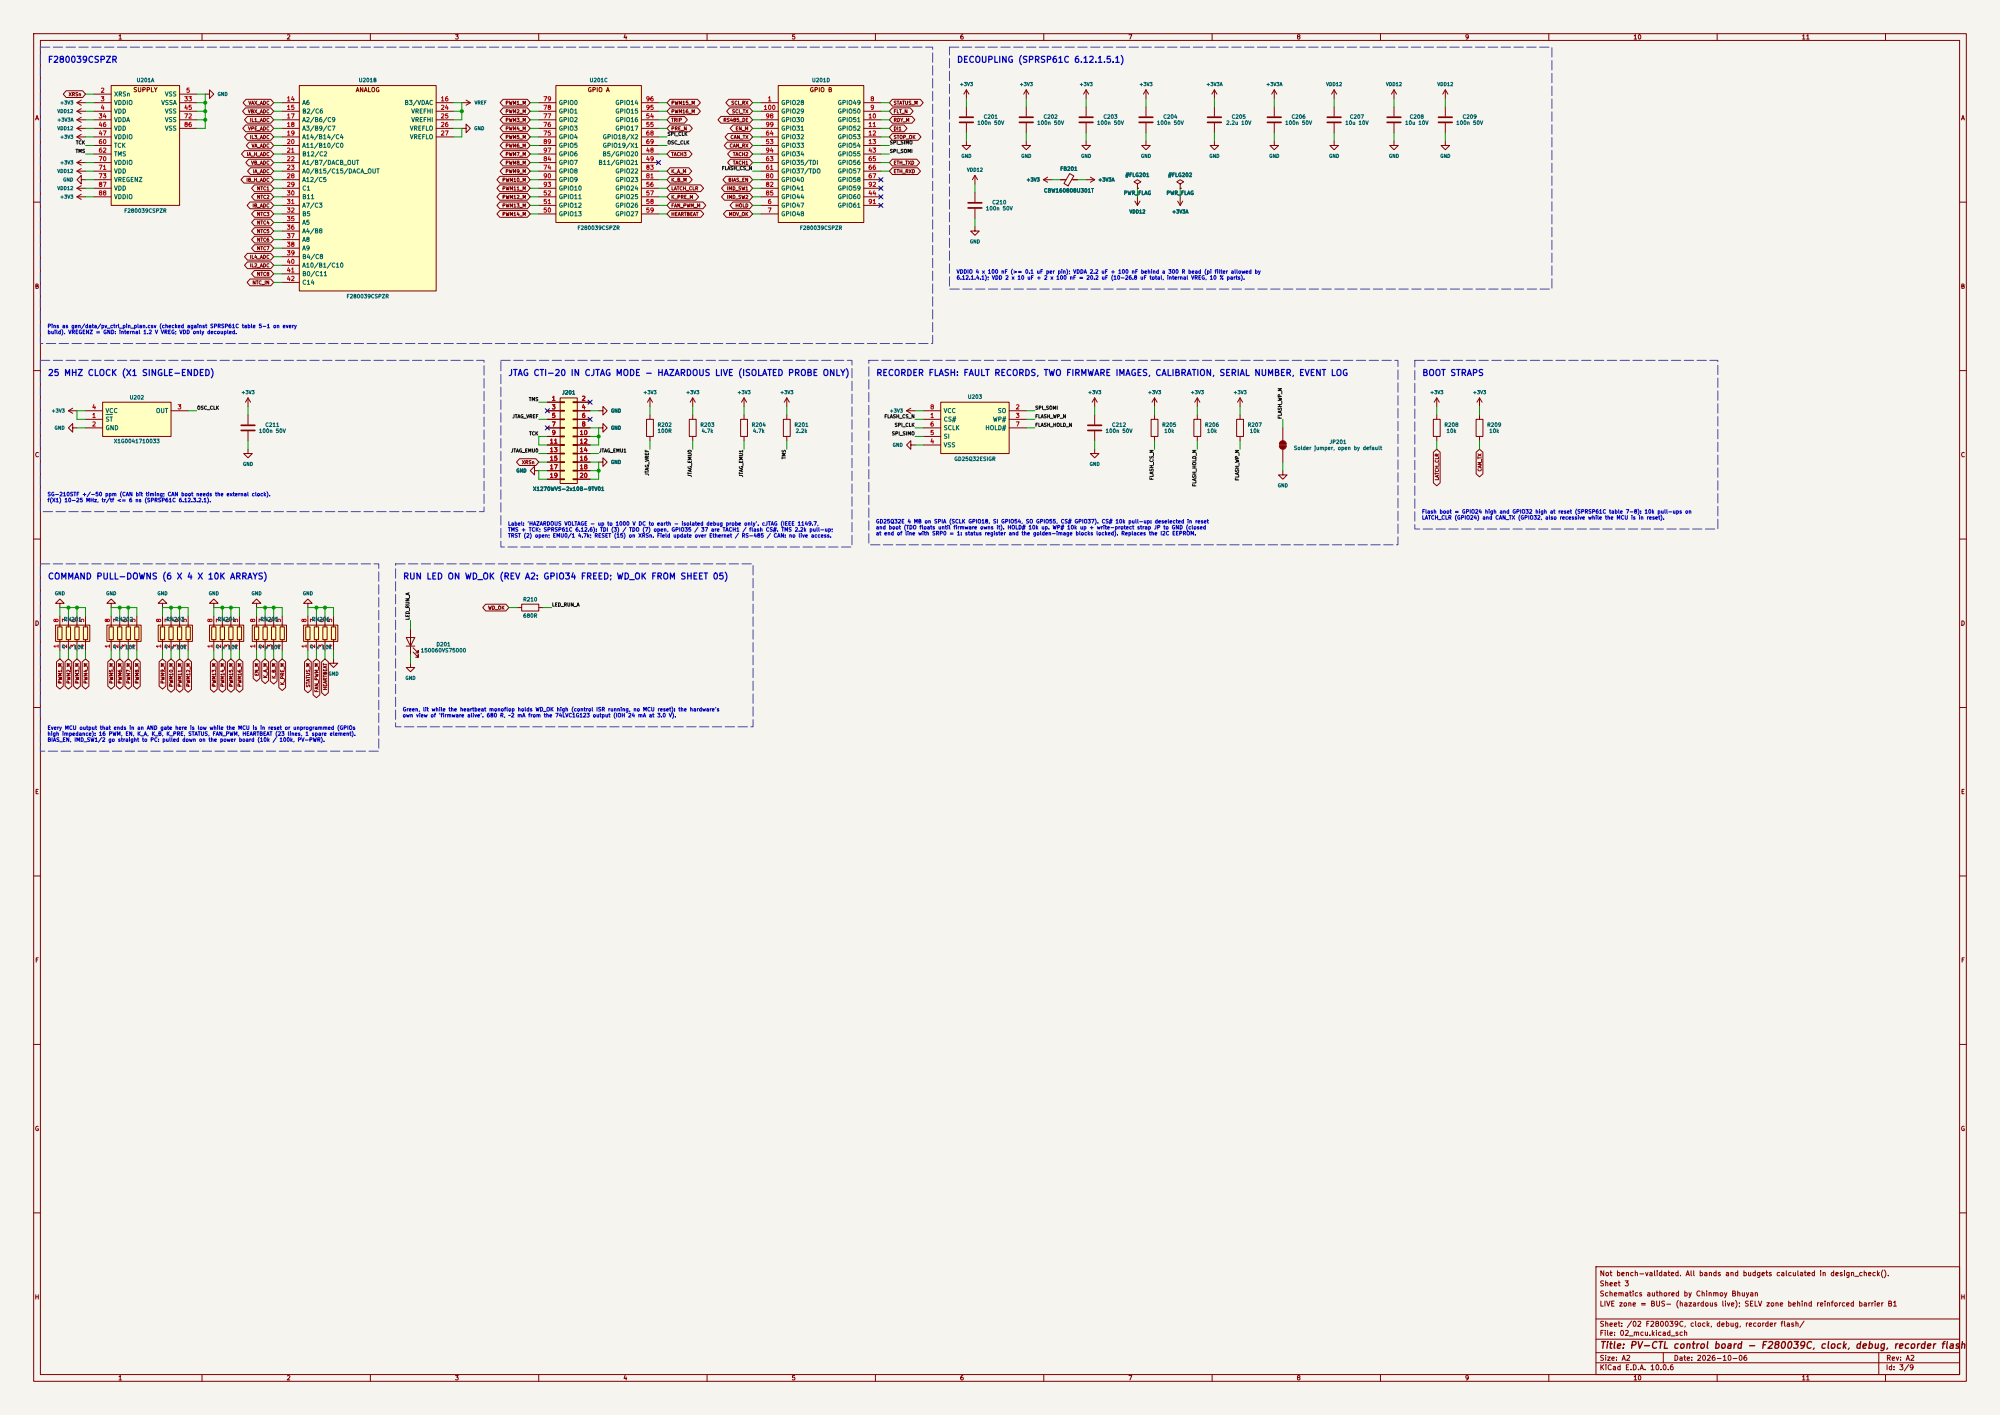
[picture p161: page 3]

VDDIO 4 x 100 nF (>= 0.1 uF per pin); VDDA 2.2 uF + 100 nF behind a 300 R bead (pi filter allowed by 6.12.1.4.1); VDD 2 x 10 uF + 2 x 100 nF = 20.2 uF (10-26.8 uF total, internal VREG, 10 % parts).

25 MHZ CLOCK (X1 SINGLE-ENDED)

JTAG CTI-20 IN CJTAG MODE - HAZARDOUS LIVE (ISOLATED PROBE ONLY)

RECORDER FLASH: FAULT RECORDS, TWO FIRMWARE IMAGES, CALIBRATION, SERIAL NUMBER, EVENT LOG

at end of line with SRP0 = 1: status register and the golden-image blocks locked). Replaces the I2C EEPROM. GND

LATCH_CLR (GPIO24) and CAN_TX (GPIO32, also recessive while the MCU is in reset).

Label: 'HAZARDOUS VOLTAGE - up to 1000 V DC to earth - isolated debug probe only'. cJTAG (IEEE 1149.7, TMS + TCK; SPRSP61C 6.12.6): TDI (3) / TDO (7) open, GPIO35 / 37 are TACH1 / flash CS#. TMS 2.2k pull-up; TRST (2) open; EMU0/1 4.7k; RESET (15) on XRSn. Field update over Ethernet / RS-485 / CAN: no live access. COMMAND PULL-DOWNS (6 X 4 X 10K ARRAYS)

GD25Q32E 4 MB on SPIA (SCLK GPIO18, SI GPIO54, SO GPIO55, CS# GPIO37). CS# 10k pull-up: deselected in reset and boot (TDO floats until firmware owns it). HOLD# 10k up. WP# 10k up + write-protect strap JP to GND (closed

RUN LED ON WD_OK (REV A2: GPIO34 FREED; WD_OK FROM SHEET 05)

Every MCU output that ends in an AND gate here is low while the MCU is in reset or unprogrammed (GPIOs
high impedance): 16 PWM, EN, K_A, K_B, K_PRE, STATUS, FAN_PWM, HEARTBEAT (23 lines, 1 spare element). BIAS_EN, IMD_SW1/2 go straight to PC: pulled down on the power board (10k / 100k, PV-PWR).

Not bench-validated. All bands and budgets calculated in design_check().
Sheet 3
Schematics authored by Chinmoy Bhuyan
LIVE zone = BUS- (hazardous live); SELV zone behind reinforced barrier B1

Sheet: /02 F280039C, clock, debug, recorder flash/
File: 02_mcu.kicad_sch
Title: PV-CTL control board - F280039C, clock, debug, recorder flash

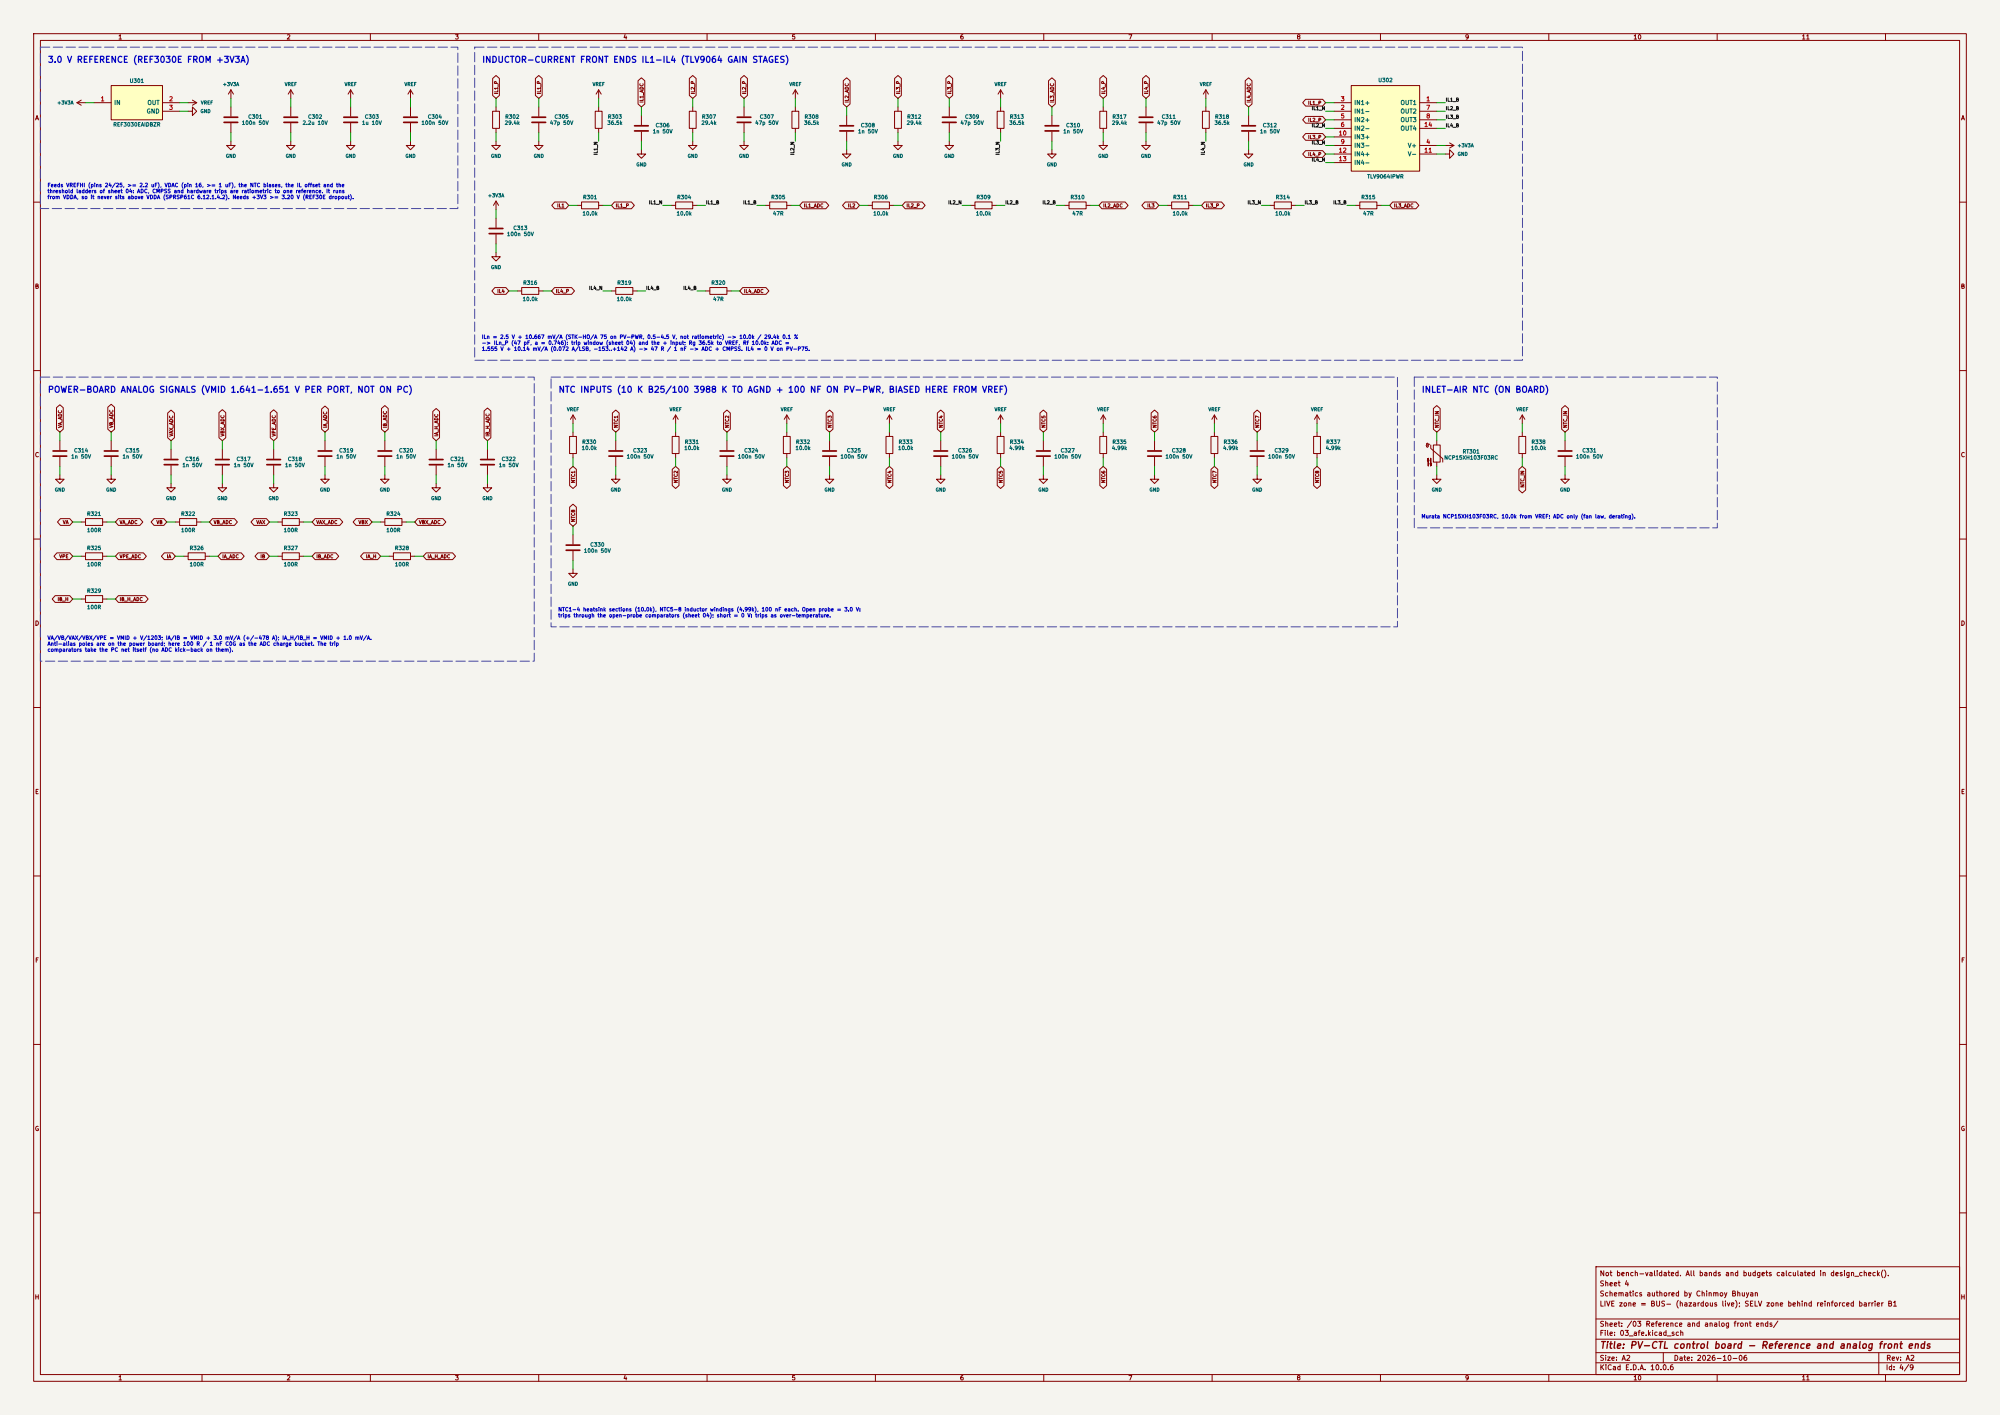
[picture p162: page 4]

INDUCTOR-CURRENT FRONT ENDS IL1-IL4 (TLV9064 GAIN STAGES)

Feeds VREFHI (pins 24/25, >= 2.2 uF), VDAC (pin 16, >= 1 uF), the NTC biases, the IL offset and the
threshold ladders of sheet 04: ADC, CMPSS and hardware trips are ratiometric to one reference. It runs
from VDDA, so it never sits above VDDA (SPRSP61C 6.12.1.4.2). Needs +3V3 >= 3.20 V (REF30E dropout).

ILn = 2.5 V + 10.667 mV/A (STK-HO/A 75 on PV-PWR, 0.5-4.5 V, not ratiometric) -> 10.0k / 29.4k 0.1 % -> ILn_P (47 pF, a = 0.746): trip window (sheet 04) and the + input; Rg 36.5k to VREF, Rf 10.0k: ADC =

POWER-BOARD ANALOG SIGNALS (VMID 1.641-1.651 V PER PORT, NOT ON PC)

NTC INPUTS (10 K B25/100 3988 K TO AGND + 100 NF ON PV-PWR, BIASED HERE FROM VREF)

INLET-AIR NTC (ON BOARD)

NTC1-4 heatsink sections (10.0k), NTC5-8 inductor windings (4.99k), 100 nF each. Open probe = 3.0 V: trips through the open-probe comparators (sheet 04); short = 0 V: trips as over-temperature.

VA/VB/VAX/VBX/VPE = VMID + V/1203; IA/IB = VMID + 3.0 mV/A (+/-478 A); IA_H/IB_H = VMID + 1.0 mV/A. Anti-alias poles are on the power board; here 100 R / 1 nF C0G as the ADC charge bucket. The trip

comparators take the PC net itself (no ADC kick-back on them).

Not bench-validated. All bands and budgets calculated in design_check().
Sheet 4

Sheet: /03 Reference and analog front ends/
File: 03_afe.kicad_sch
Title: PV-CTL control board - Reference and analog front ends

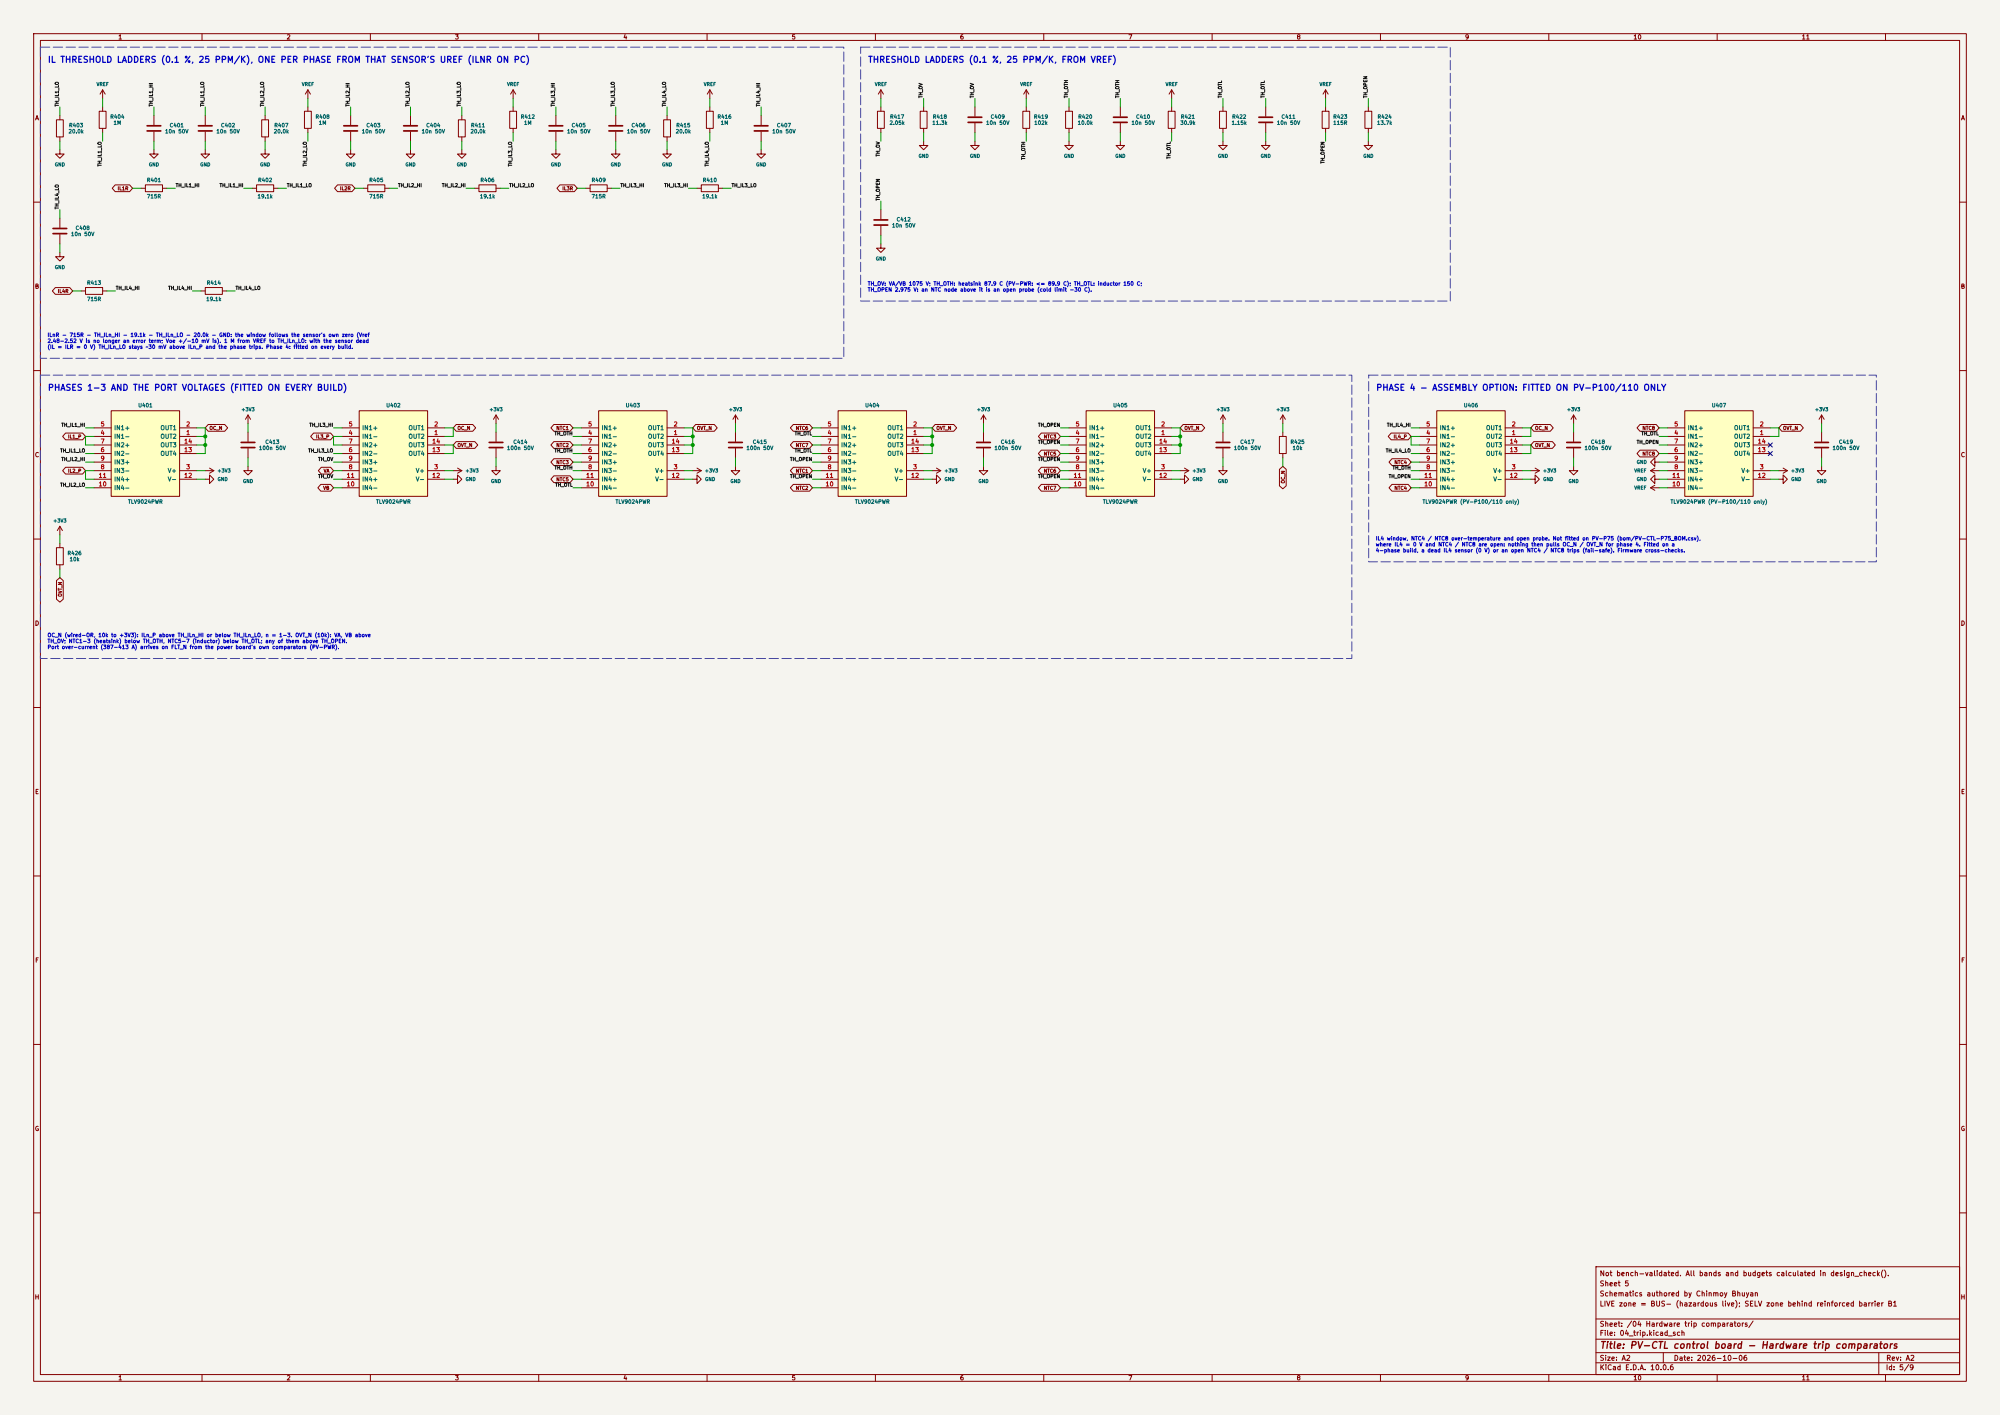
[picture p163: page 5]

IL THRESHOLD LADDERS (0.1 %, 25 PPM/K), ONE PER PHASE FROM THAT SENSOR'S UREF (ILNR ON PC)

THRESHOLD LADDERS (0.1 %, 25 PPM/K, FROM VREF)

TH_OV: VA/VB 1075 V; TH_OTH: heatsink 87.9 C (PV-PWR: <= 89.9 C); TH_OTL: inductor 150 C; TH_OPEN 2.975 V: an NTC node above it is an open probe (cold limit -30 C).

ILnR - 715R - TH_ILn_HI - 19.1k - TH_ILn_LO - 20.0k - GND: the window follows the sensor's own zero (Vref 2.48-2.52 V is no longer an error term; Voe +/-10 mV is). 1 M from VREF to TH_ILn_LO: with the sensor dead

(IL = ILR = 0 V) TH_ILn_LO stays ~30 mV above ILn_P and the phase trips. Phase 4: fitted on every build.

PHASES 1-3 AND THE PORT VOLTAGES (FITTED ON EVERY BUILD)

PHASE 4 - ASSEMBLY OPTION: FITTED ON PV-P100/110 ONLY

IL4 window, NTC4 / NTC8 over-temperature and open probe. Not fitted on PV-P75 (bom/PV-CTL-P75_BOM.csv), where IL4 = 0 V and NTC4 / NTC8 are open: nothing then pulls OC_N / OVT_N for phase 4. Fitted on a 4-phase build, a dead IL4 sensor (0 V) or an open NTC4 / NTC8 trips (fail-safe). Firmware cross-checks.

OC_N (wired-OR, 10k to +3V3): ILn_P above TH_ILn_HI or below TH_ILn_LO, n = 1-3. OVT_N (10k): VA, VB above
TH_OV; NTC1-3 (heatsink) below TH_OTH, NTC5-7 (inductor) below TH_OTL; any of them above TH_OPEN. Port over-current (387-413 A) arrives on FLT_N from the power board's own comparators (PV-PWR).

Not bench-validated. All bands and budgets calculated in design_check().
Sheet 5

Sheet: /04 Hardware trip comparators/
File: 04_trip.kicad_sch
Title: PV-CTL control board - Hardware trip comparators

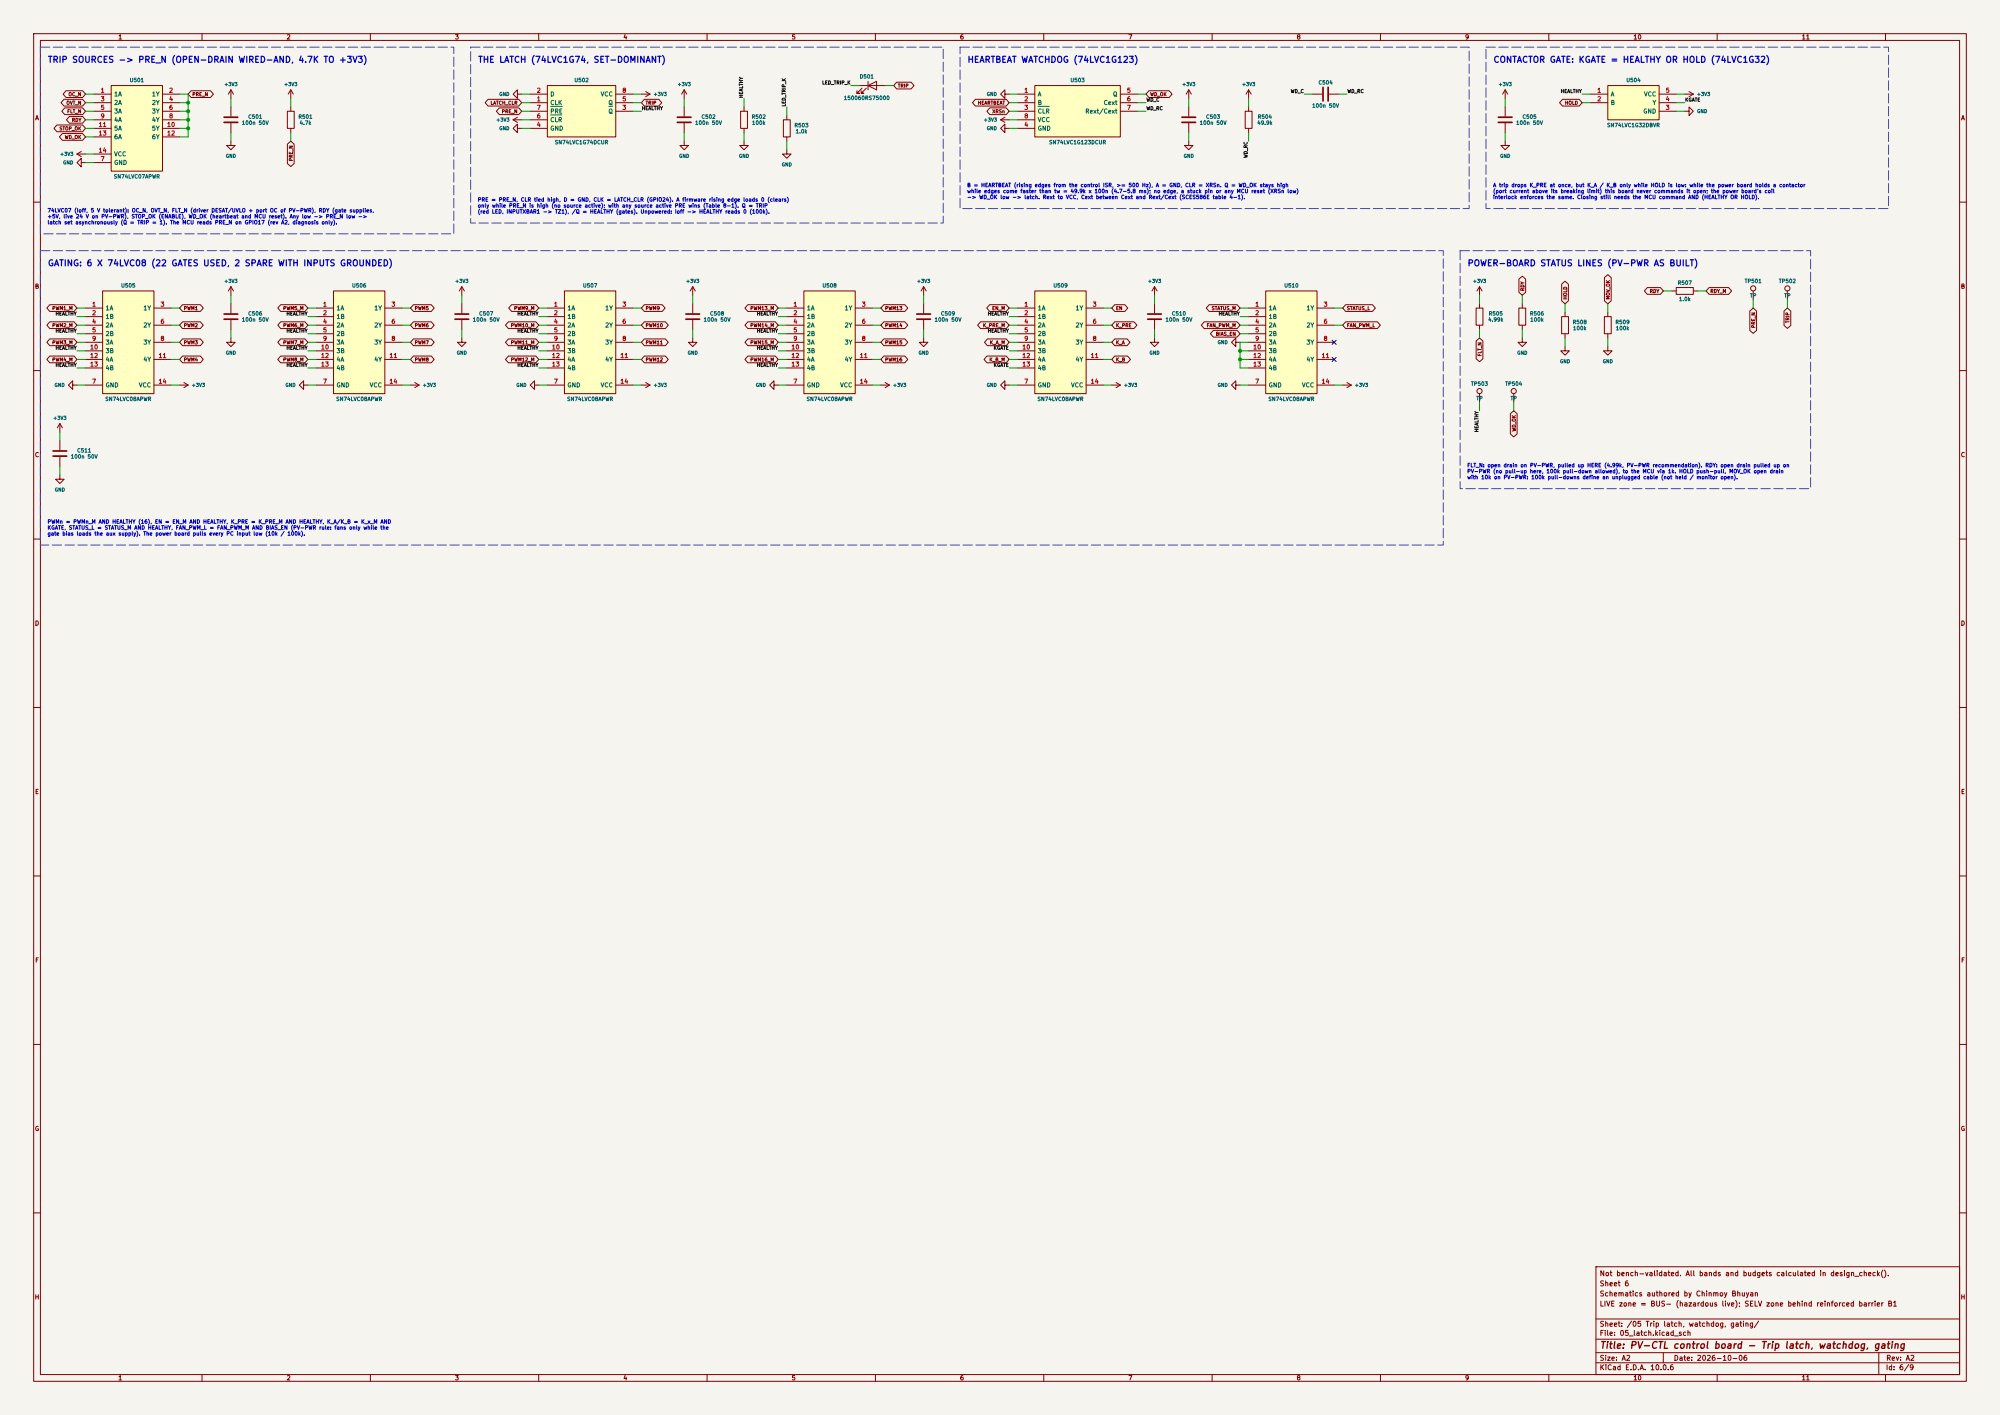
[picture p164: page 6]

A trip drops K_PRE at once, but K_A / K_B only while HOLD is low: while the power board holds a contactor (port current above its breaking limit) this board never commands it open; the power board's coil

interlock enforces the same. Closing still needs the MCU command AND (HEALTHY OR HOLD).

PRE = PRE_N, CLR tied high, D = GND, CLK = LATCH_CLR (GPIO24). A firmware rising edge loads 0 (clears)
only while PRE_N is high (no source active); with any source active PRE wins (Table 8-1). Q = TRIP

74LVC07 (Ioff, 5 V tolerant): OC_N, OVT_N, FLT_N (driver DESAT/UVLO + port OC of PV-PWR), RDY (gate supplies, +5V, live 24 V on PV-PWR), STOP_OK (ENABLE), WD_OK (heartbeat and MCU reset). Any low -> PRE_N low ->

latch set asynchronously (Q = TRIP = 1). The MCU reads PRE_N on GPIO17 (rev A2, diagnosis only).

GATING: 6 X 74LVC08 (22 GATES USED, 2 SPARE WITH INPUTS GROUNDED)

POWER-BOARD STATUS LINES (PV-PWR AS BUILT)

FLT_N: open drain on PV-PWR, pulled up HERE (4.99k, PV-PWR recommendation). RDY: open drain pulled up on PV-PWR (no pull-up here, 100k pull-down allowed), to the MCU via 1k. HOLD push-pull, MOV_OK open drain with 10k on PV-PWR: 100k pull-downs define an unplugged cable (not held / monitor open).

PWMn = PWMn_M AND HEALTHY (16), EN = EN_M AND HEALTHY, K_PRE = K_PRE_M AND HEALTHY, K_A/K_B = K_x_M AND
KGATE, STATUS_L = STATUS_M AND HEALTHY, FAN_PWM_L = FAN_PWM_M AND BIAS_EN (PV-PWR rule: fans only while the gate bias loads the aux supply). The power board pulls every PC input low (10k / 100k).

Not bench-validated. All bands and budgets calculated in design_check().
Sheet 6

Sheet: /05 Trip latch, watchdog, gating/
File: 05_latch.kicad_sch
Title: PV-CTL control board - Trip latch, watchdog, gating

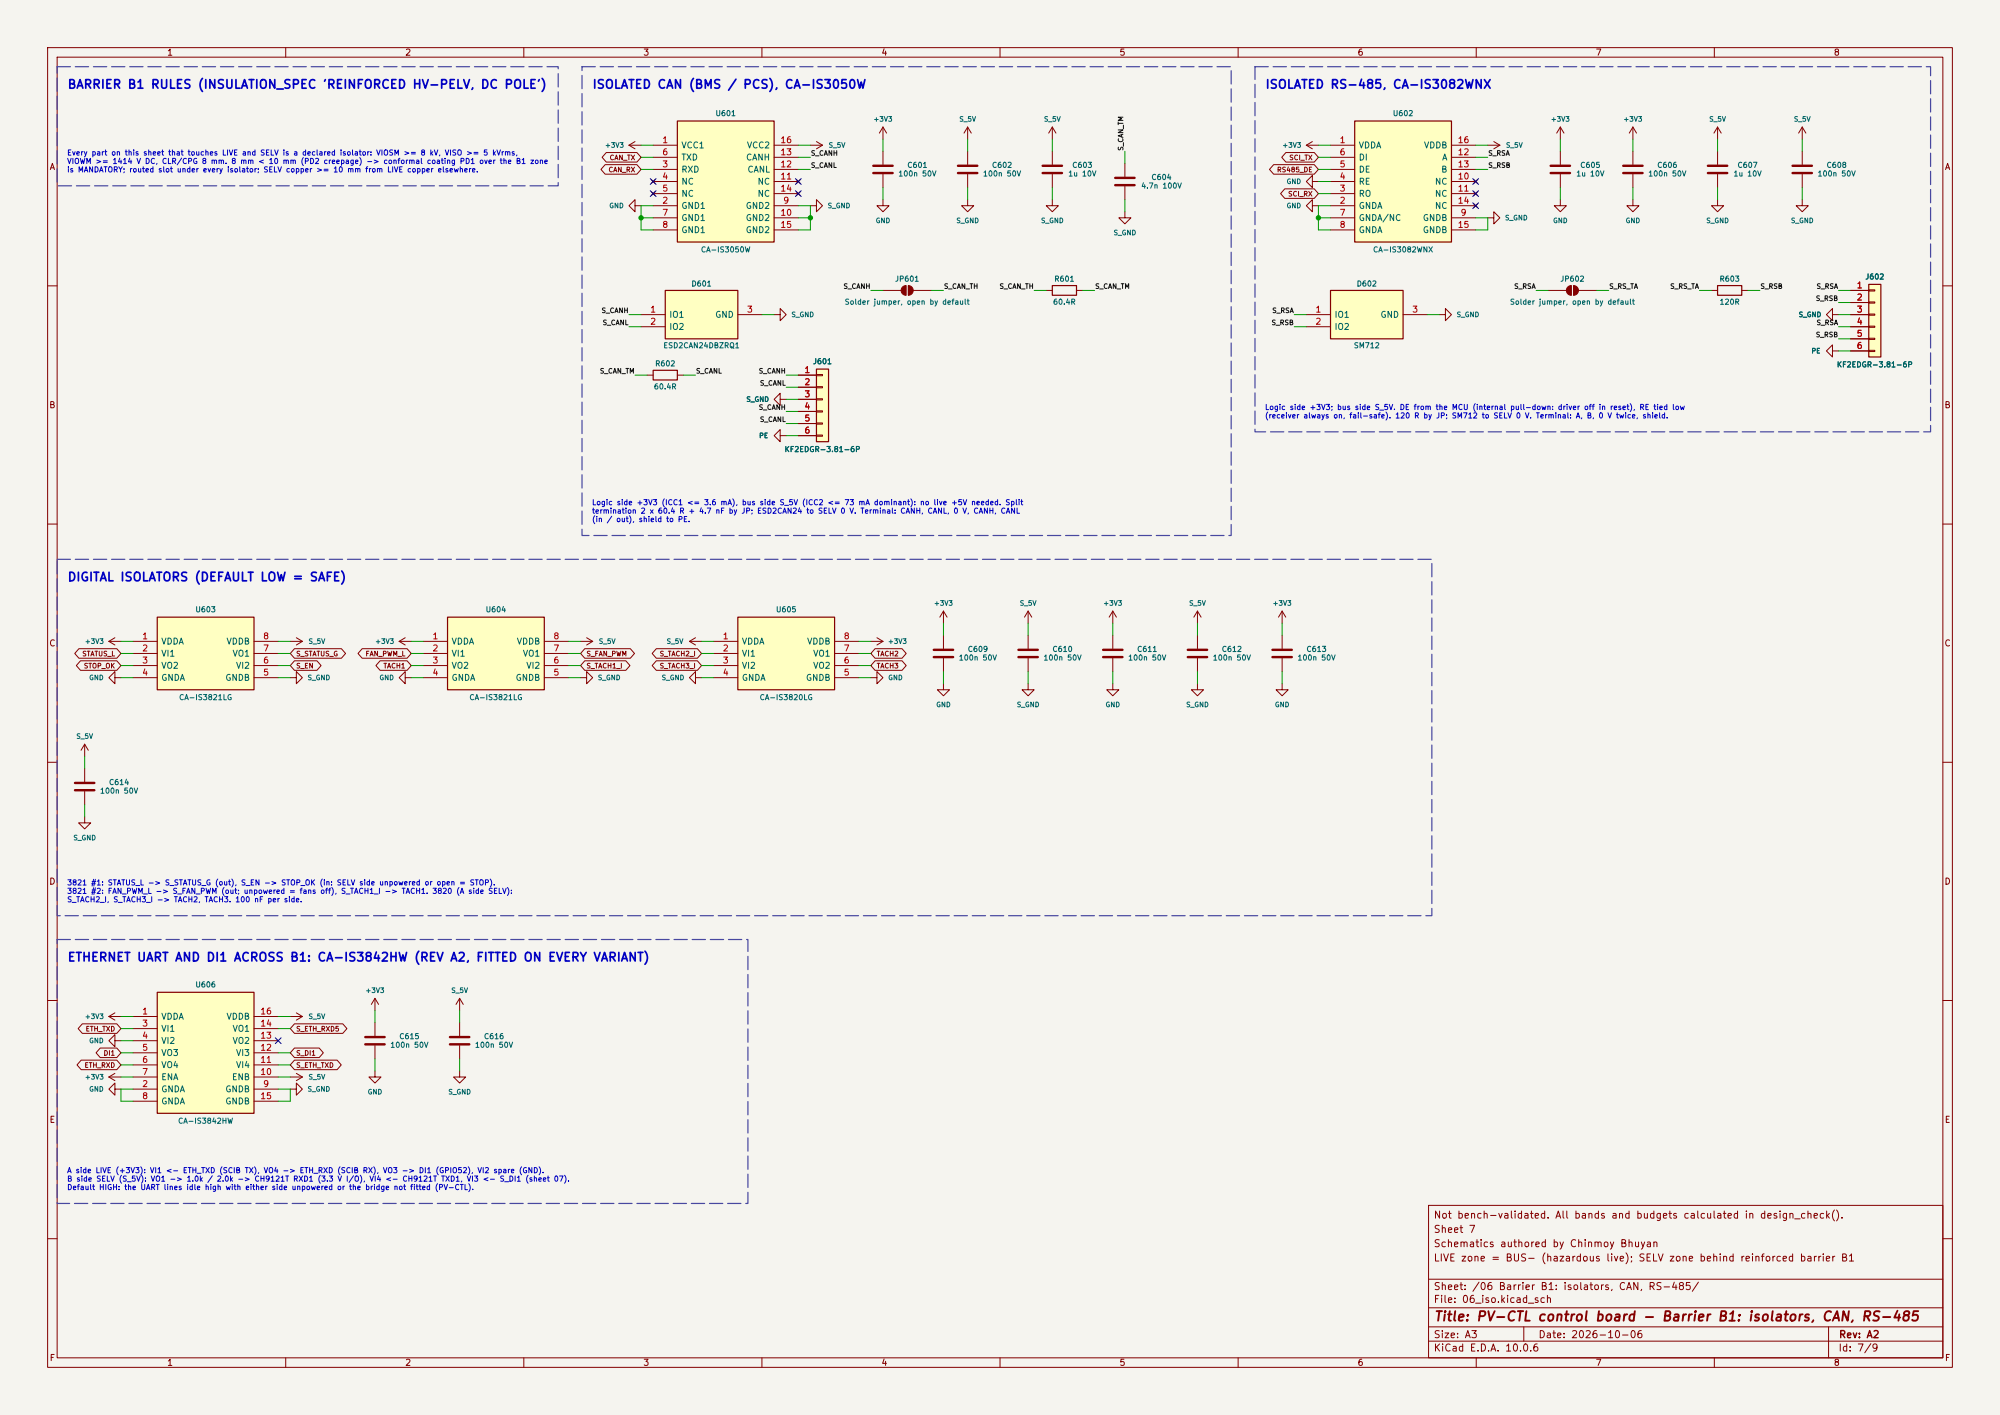
[picture p165: page 7]

is MANDATORY; routed slot under every isolator; SELV copper >= 10 mm from LIVE copper elsewhere. BARRIER B1 RULES (INSULATION_SPEC 'REINFORCED HV-PELV, DC POLE')

ISOLATED CAN (BMS / PCS), CA-IS3050W

Every part on this sheet that touches LIVE and SELV is a declared isolator: VIOSM >= 8 kV, VISO >= 5 kVrms, VIOWM >= 1414 V DC, CLR/CPG 8 mm. 8 mm < 10 mm (PD2 creepage) -> conformal coating PD1 over the B1 zone

S_RS_TA DIGITAL ISOLATORS (DEFAULT LOW = SAFE)

Logic side +3V3; bus side S_5V. DE from the MCU (internal pull-down: driver off in reset), RE tied low

(receiver always on, fail-safe). 120 R by JP; SM712 to SELV 0 V. Terminal: A, B, 0 V twice, shield. ETHERNET UART AND DI1 ACROSS B1: CA-IS3842HW (REV A2, FITTED ON EVERY VARIANT)

Logic side +3V3 (ICC1 <= 3.6 mA), bus side S_5V (ICC2 <= 73 mA dominant): no live +5V needed. Split
termination 2 x 60.4 R + 4.7 nF by JP; ESD2CAN24 to SELV 0 V. Terminal: CANH, CANL, 0 V, CANH, CANL
(in / out), shield to PE.

3821 #1: STATUS_L -> S_STATUS_G (out), S_EN -> STOP_OK (in: SELV side unpowered or open = STOP). 3821 #2: FAN_PWM_L -> S_FAN_PWM (out; unpowered = fans off), S_TACH1_I -> TACH1. 3820 (A side SELV): S_TACH2_I, S_TACH3_I -> TACH2, TACH3. 100 nF per side.

A side LIVE (+3V3): VI1 <- ETH_TXD (SCIB TX), VO4 -> ETH_RXD (SCIB RX), VO3 -> DI1 (GPIO52), VI2 spare (GND). B side SELV (S_5V): VO1 -> 1.0k / 2.0k -> CH9121T RXD1 (3.3 V I/O), VI4 <- CH9121T TXD1, VI3 <- S_DI1 (sheet 07). Default HIGH: the UART lines idle high with either side unpowered or the bridge not fitted (PV-CTL).

Not bench-validated. All bands and budgets calculated in design_check().
Sheet 7
Schematics authored by Chinmoy Bhuyan
LIVE zone = BUS- (hazardous live); SELV zone behind reinforced barrier B1

Sheet: /06 Barrier B1: isolators, CAN, RS-485/
File: 06_iso.kicad_sch
Title: PV-CTL control board - Barrier B1: isolators, CAN, RS-485

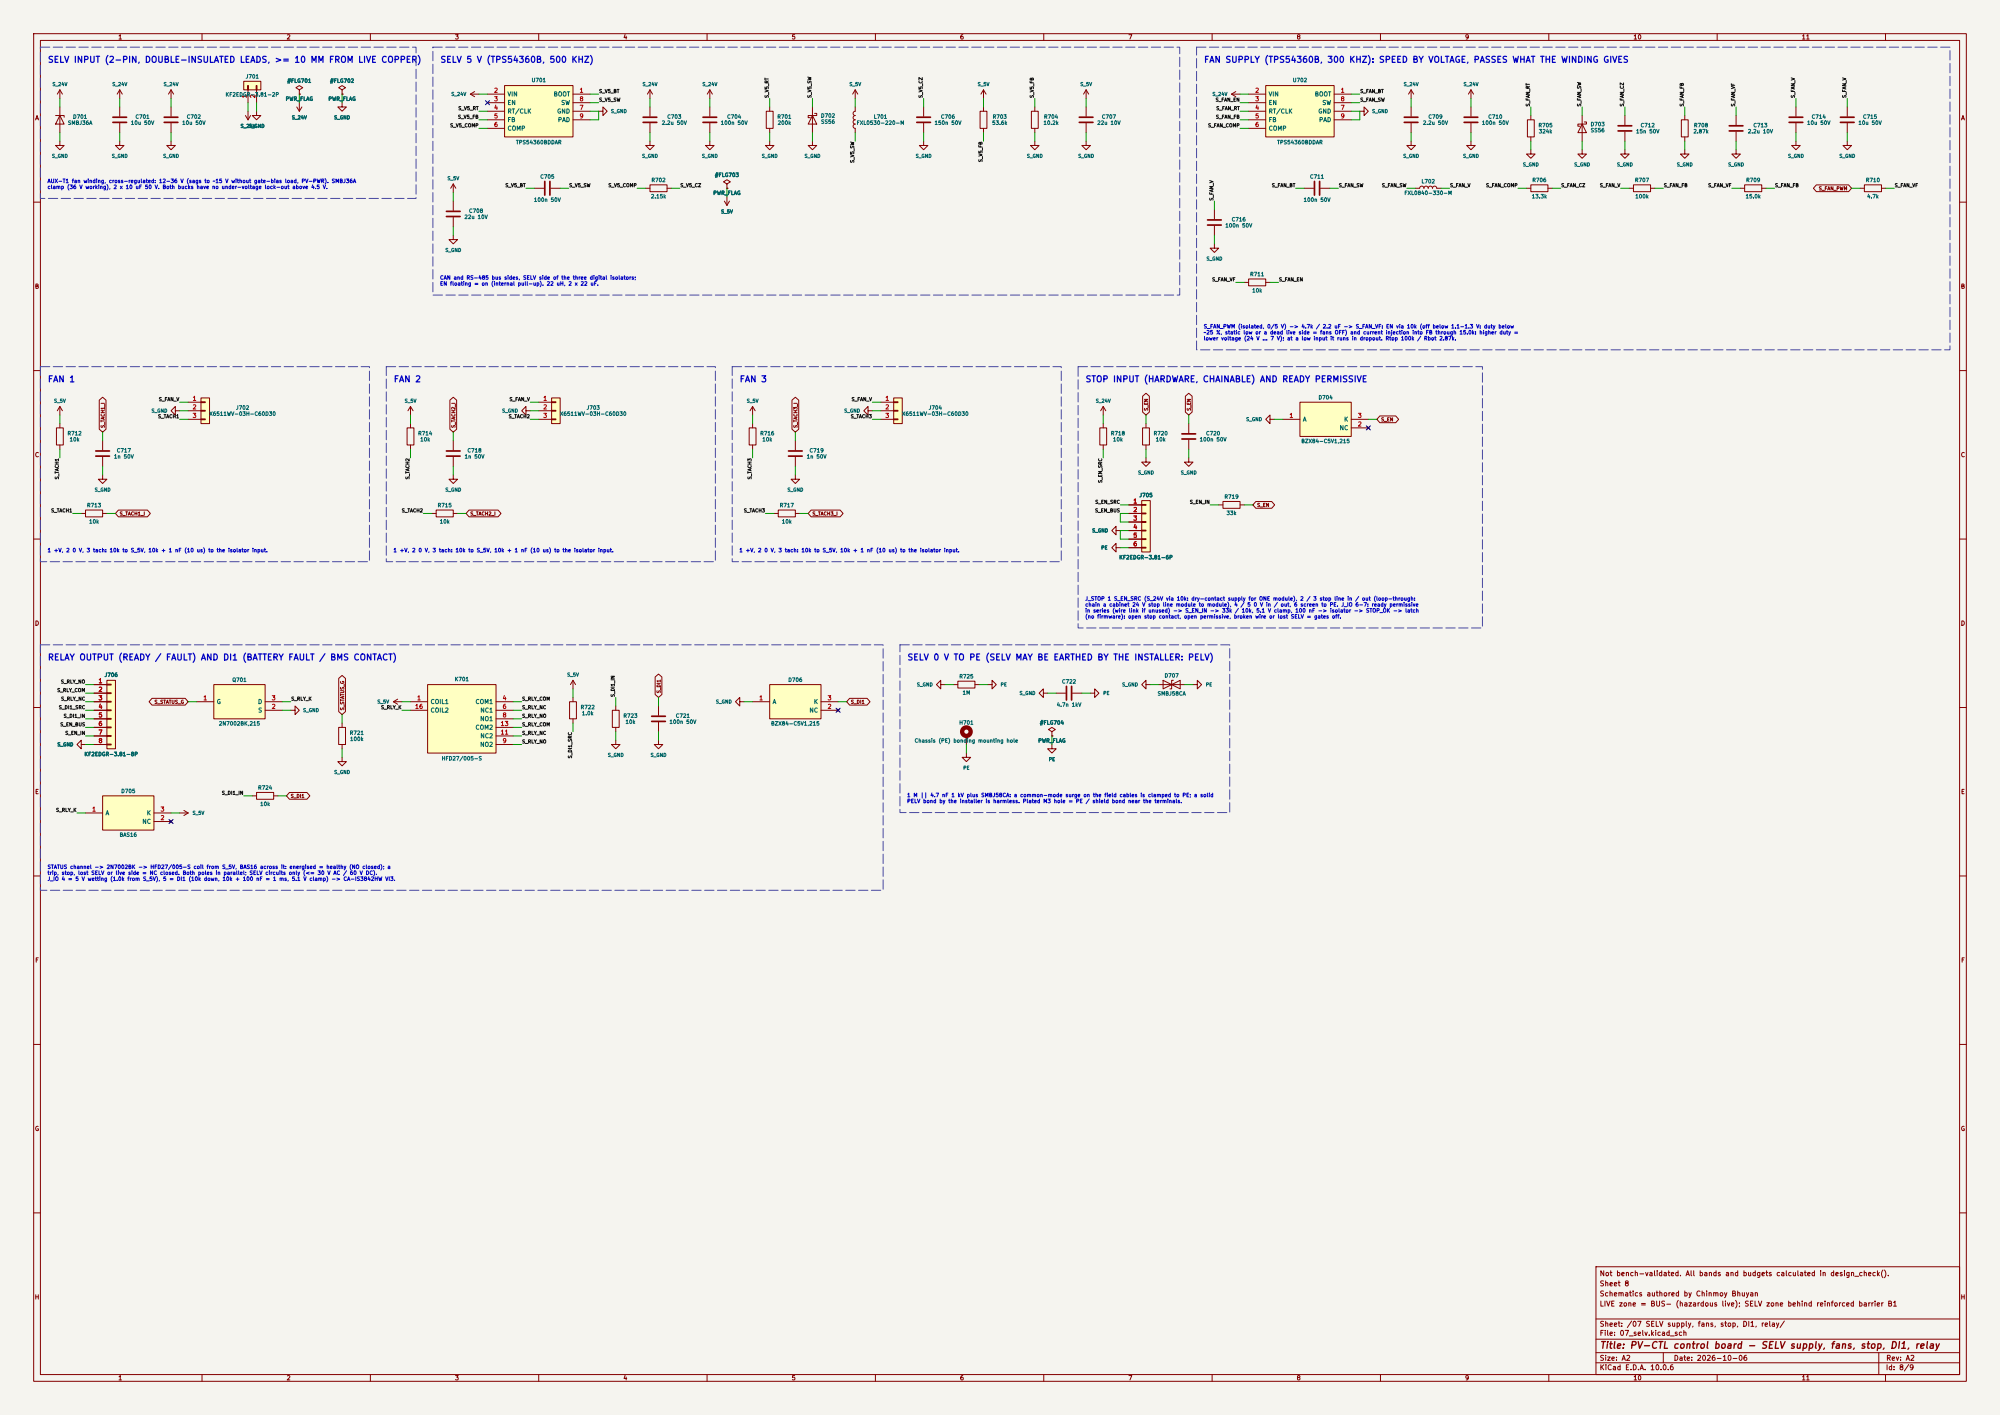
[picture p166: page 8]

SELV INPUT (2-PIN, DOUBLE-INSULATED LEADS, >= 10 MM FROM LIVE COPPER)

FAN SUPPLY (TPS54360B, 300 KHZ): SPEED BY VOLTAGE, PASSES WHAT THE WINDING GIVES

AUX-T1 fan winding, cross-regulated: 12-36 V (sags to ~15 V without gate-bias load, PV-PWR). SMBJ36A

CAN and RS-485 bus sides, SELV side of the three digital isolators; EN floating = on (internal pull-up). 22 uH, 2 x 22 uF. FAN 1

S_FAN_PWM (isolated, 0/5 V) -> 4.7k / 2.2 uF -> S_FAN_VF: EN via 10k (off below 1.1-1.3 V: duty below
~25 %, static low or a dead live side = fans OFF) and current injection into FB through 15.0k: higher duty =
lower voltage (24 V ... 7 V); at a low input it runs in dropout. Rtop 100k / Rbot 2.87k.

STOP INPUT (HARDWARE, CHAINABLE) AND READY PERMISSIVE

1 +V, 2 0 V, 3 tach: 10k to S_5V, 10k + 1 nF (10 us) to the isolator input.

J_STOP 1 S_EN_SRC (S_24V via 10k: dry-contact supply for ONE module), 2 / 3 stop line in / out (loop-through: chain a cabinet 24 V stop line module to module), 4 / 5 0 V in / out, 6 screen to PE. J_IO 6-7: ready permissive

in series (wire link if unused) -> S_EN_IN -> 33k / 10k, 5.1 V clamp, 100 nF -> isolator -> STOP_OK -> latch
(no firmware): open stop contact, open permissive, broken wire or lost SELV = gates off.

RELAY OUTPUT (READY / FAULT) AND DI1 (BATTERY FAULT / BMS CONTACT)

H701 Chassis (PE) bonding mounting hole

STATUS channel -> 2N7002BK -> HFD27/005-S coil from S_5V, BAS16 across it: energised = healthy (NO closed); a
trip, stop, lost SELV or live side = NC closed. Both poles in parallel; SELV circuits only (<= 30 V AC / 60 V DC). J_IO 4 = 5 V wetting (1.0k from S_5V), 5 = DI1 (10k down, 10k + 100 nF = 1 ms, 5.1 V clamp) -> CA-IS3842HW VI3.

Not bench-validated. All bands and budgets calculated in design_check().
Sheet 8

Sheet: /07 SELV supply, fans, stop, DI1, relay/
File: 07_selv.kicad_sch
Title: PV-CTL control board - SELV supply, fans, stop, DI1, relay

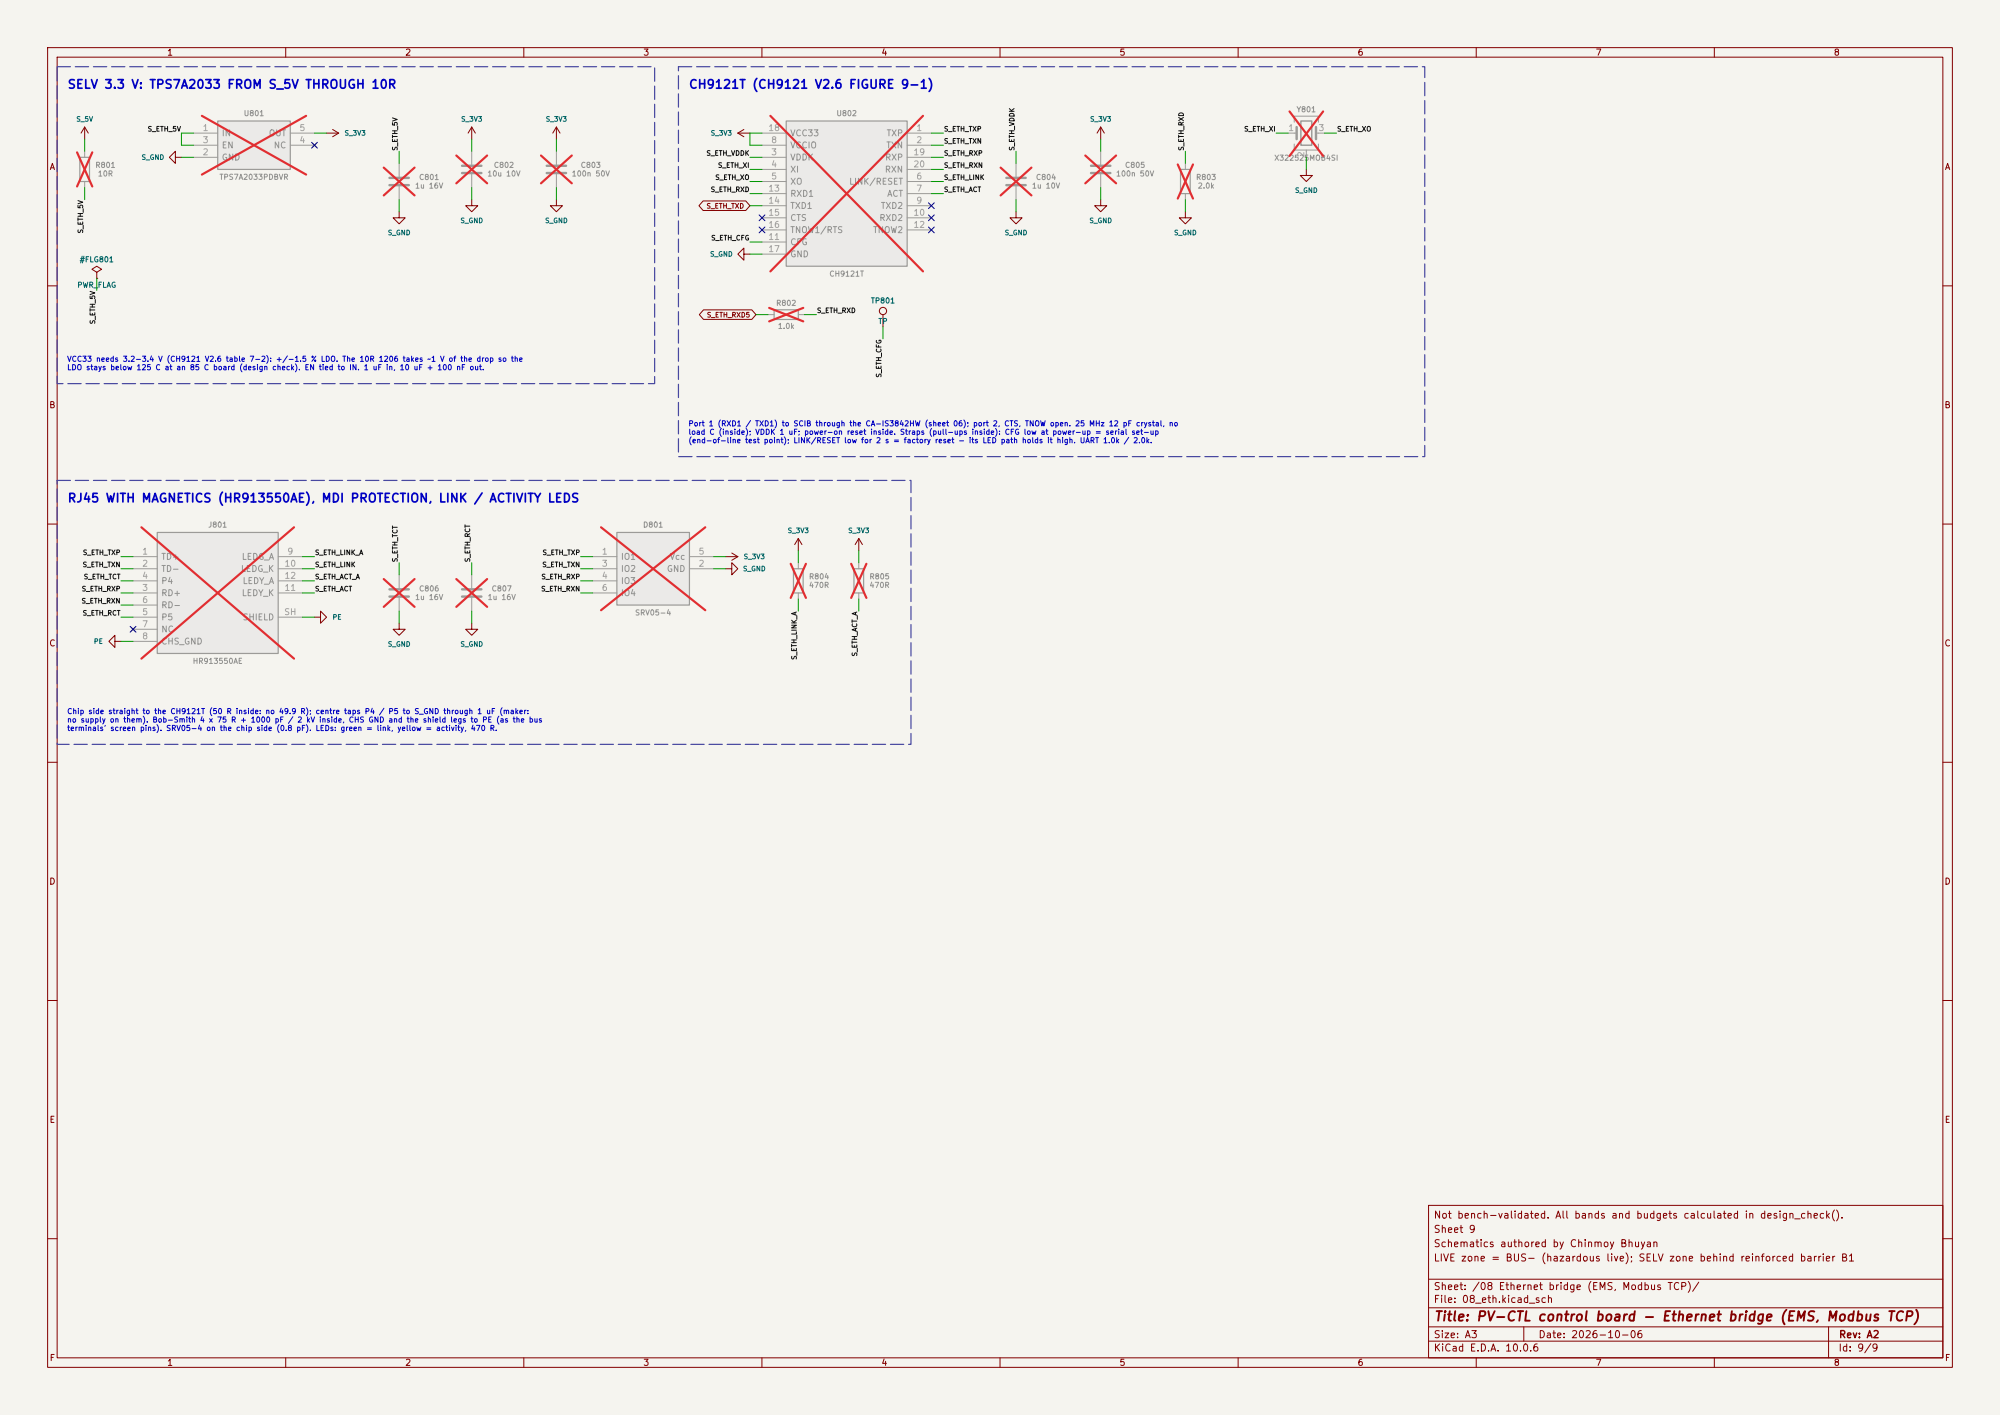
[picture p167: page 9]

VCC33 needs 3.2-3.4 V (CH9121 V2.6 table 7-2): +/-1.5 % LDO. The 10R 1206 takes ~1 V of the drop so the
LDO stays below 125 C at an 85 C board (design check). EN tied to IN. 1 uF in, 10 uF + 100 nF out.

Port 1 (RXD1 / TXD1) to SCIB through the CA-IS3842HW (sheet 06); port 2, CTS, TNOW open. 25 MHz 12 pF crystal, no
load C (inside); VDDK 1 uF; power-on reset inside. Straps (pull-ups inside): CFG low at power-up = serial set-up

(end-of-line test point); LINK/RESET low for 2 s = factory reset - its LED path holds it high. UART 1.0k / 2.0k. RJ45 WITH MAGNETICS (HR913550AE), MDI PROTECTION, LINK / ACTIVITY LEDS

Chip side straight to the CH9121T (50 R inside: no 49.9 R); centre taps P4 / P5 to S_GND through 1 uF (maker: no supply on them). Bob-Smith 4 x 75 R + 1000 pF / 2 kV inside, CHS GND and the shield legs to PE (as the bus

terminals' screen pins). SRV05-4 on the chip side (0.8 pF). LEDs: green = link, yellow = activity, 470 R.

Not bench-validated. All bands and budgets calculated in design_check().
Sheet 9
Schematics authored by Chinmoy Bhuyan
LIVE zone = BUS- (hazardous live); SELV zone behind reinforced barrier B1

Sheet: /08 Ethernet bridge (EMS, Modbus TCP)/
File: 08_eth.kicad_sch
Title: PV-CTL control board - Ethernet bridge (EMS, Modbus TCP)
