vectivolt/PCM/hardware/PV-PORT/outputs/PV-PORT_schematic.pdf

1 | 2 | 3 | 4 | 5 | 6 | 7 | 8

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
Size: A3 | Rev: F0 | F Date: 2026-10-04
KiCad E.D.A. 10.0.6 | Id: 1/7

# Title: PV-PORT 135 A port board - Cover / Hierarchy

## File: PV-PORT.kicad_sch

## Sheet: /

## HV-PELV reinforced (1000 VDC, OVC II, PD2, coated to PD1); HV-PE basic + bonding

## Schematics authored by Chinmoy Bhuyan

## Sheet 1

## Not bench-validated. Values: sim/port_design.py -> port_spec.json

## 06 Insulation measurement File: sheets/06_imd.kicad_sch 01 Connectors and sensor supply

File: sheets/01_io.kicad_sch | 02 Port A power path

File: sheets/02_portA_power.kicad_sch

## 05 Port B sensing and hold logic

File: sheets/05_portB_sense.kicad_sch

## 03 Port A sensing and hold logic

File: sheets/03_portA_sense.kicad_sch

## 04 Port B power path

File: sheets/04_portB_power.kicad_sch

Rev F0 | 2026-10-04 | Schematics authored by Chinmoy Bhuyan | Ports A (PV) and B (bus/battery) of PV-P75, common negative BUS-

Terminals, fuses, SPD, EMI filter, contactor, precharge relay, coil drives, hold stage, shunt, discharge + time limit, bleeder PV-PORT 135 A port board

AUX1 = V(PE-BUS-), AUX2 = V(PE-A+) (AMC3330); 992 k test strings A+ -> PE, BUS- -> PE, each with a common-source SiC pair (TPSI3050) PORT 26-way to CTRL-C2000, 14-way to SYS-IO-AUX, ID + hold readback, +24V -> +3V3S buck, AGND tie, PE bond

drawn here with their real MPN or an RFQ / CUSTOM specification.

varistor network and branch fuses are in the closed PD2 compartment.

VB bus side, VBX terminal side (AMC3330), IB current (AMC3302), two-channel hold logic, proof-test injection, readback RB1/RB2

Isolators (checked on every build): AMC3330/AMC3302, TPSI3050-Q1, CNY65B, contactor and relay coil-contact. Declared HV-PE crossings: MOV3 of each varistor Y, Y capacitors, the PE-side SiC of each insulation-measurement pair, the PE-end element of the AUX dividers.
IC-17/IC-18: the whole board is conformal-coated to PD1 (IEC 60664-3 Type 1) over all HV copper and every HV-PELV isolator footprint (8-8.5 mm packages < 10 mm reinforced at PD2). Only the NH fuse links / bases and the DC terminals sit in the cooling-air path (PD3); the board,

SYS-IO-AUX: K_DISCH energised first at power-up; the port block itself inhibits the discharge of a closed port. Coil flyback never reaches the DO clamps in normal operation (two-switch coil drives, varistor / zener across each coil).

Surge credit (D-032, IC-01/02/03): the on-board varistor Y limits pole-PE and pole-pole to 3.8 kV at In 3 kA (calculated) and is monitored: reinforced is dimensioned for 6 kV (AMC3302 6.25 kV, AMC3330 7.7 kV pass on this case only). IC-04 OPEN: the G7L coil-contact rating (4000 V AC) is below reinforced - fix in rev F1 (own isolated coil supply).

Common negative: port A and port B share BUS- (non-isolated buck-boost), so both ports are one HV domain; the main contactors switch the + pole only, fuses are in both poles. Chassis-mounted parts (terminals, fuses, CM choke, contactors, RST 200 resistors, thermostats, shunt) are

VA bus side, VAX terminal side (AMC3330), IA current (AMC3302), two-channel hold logic, proof-test injection, readback RB1/RB2 Terminals, fuses, SPD, EMI filter, contactor, precharge relay, coil drives, hold stage, shunt, discharge + time limit, bleeder

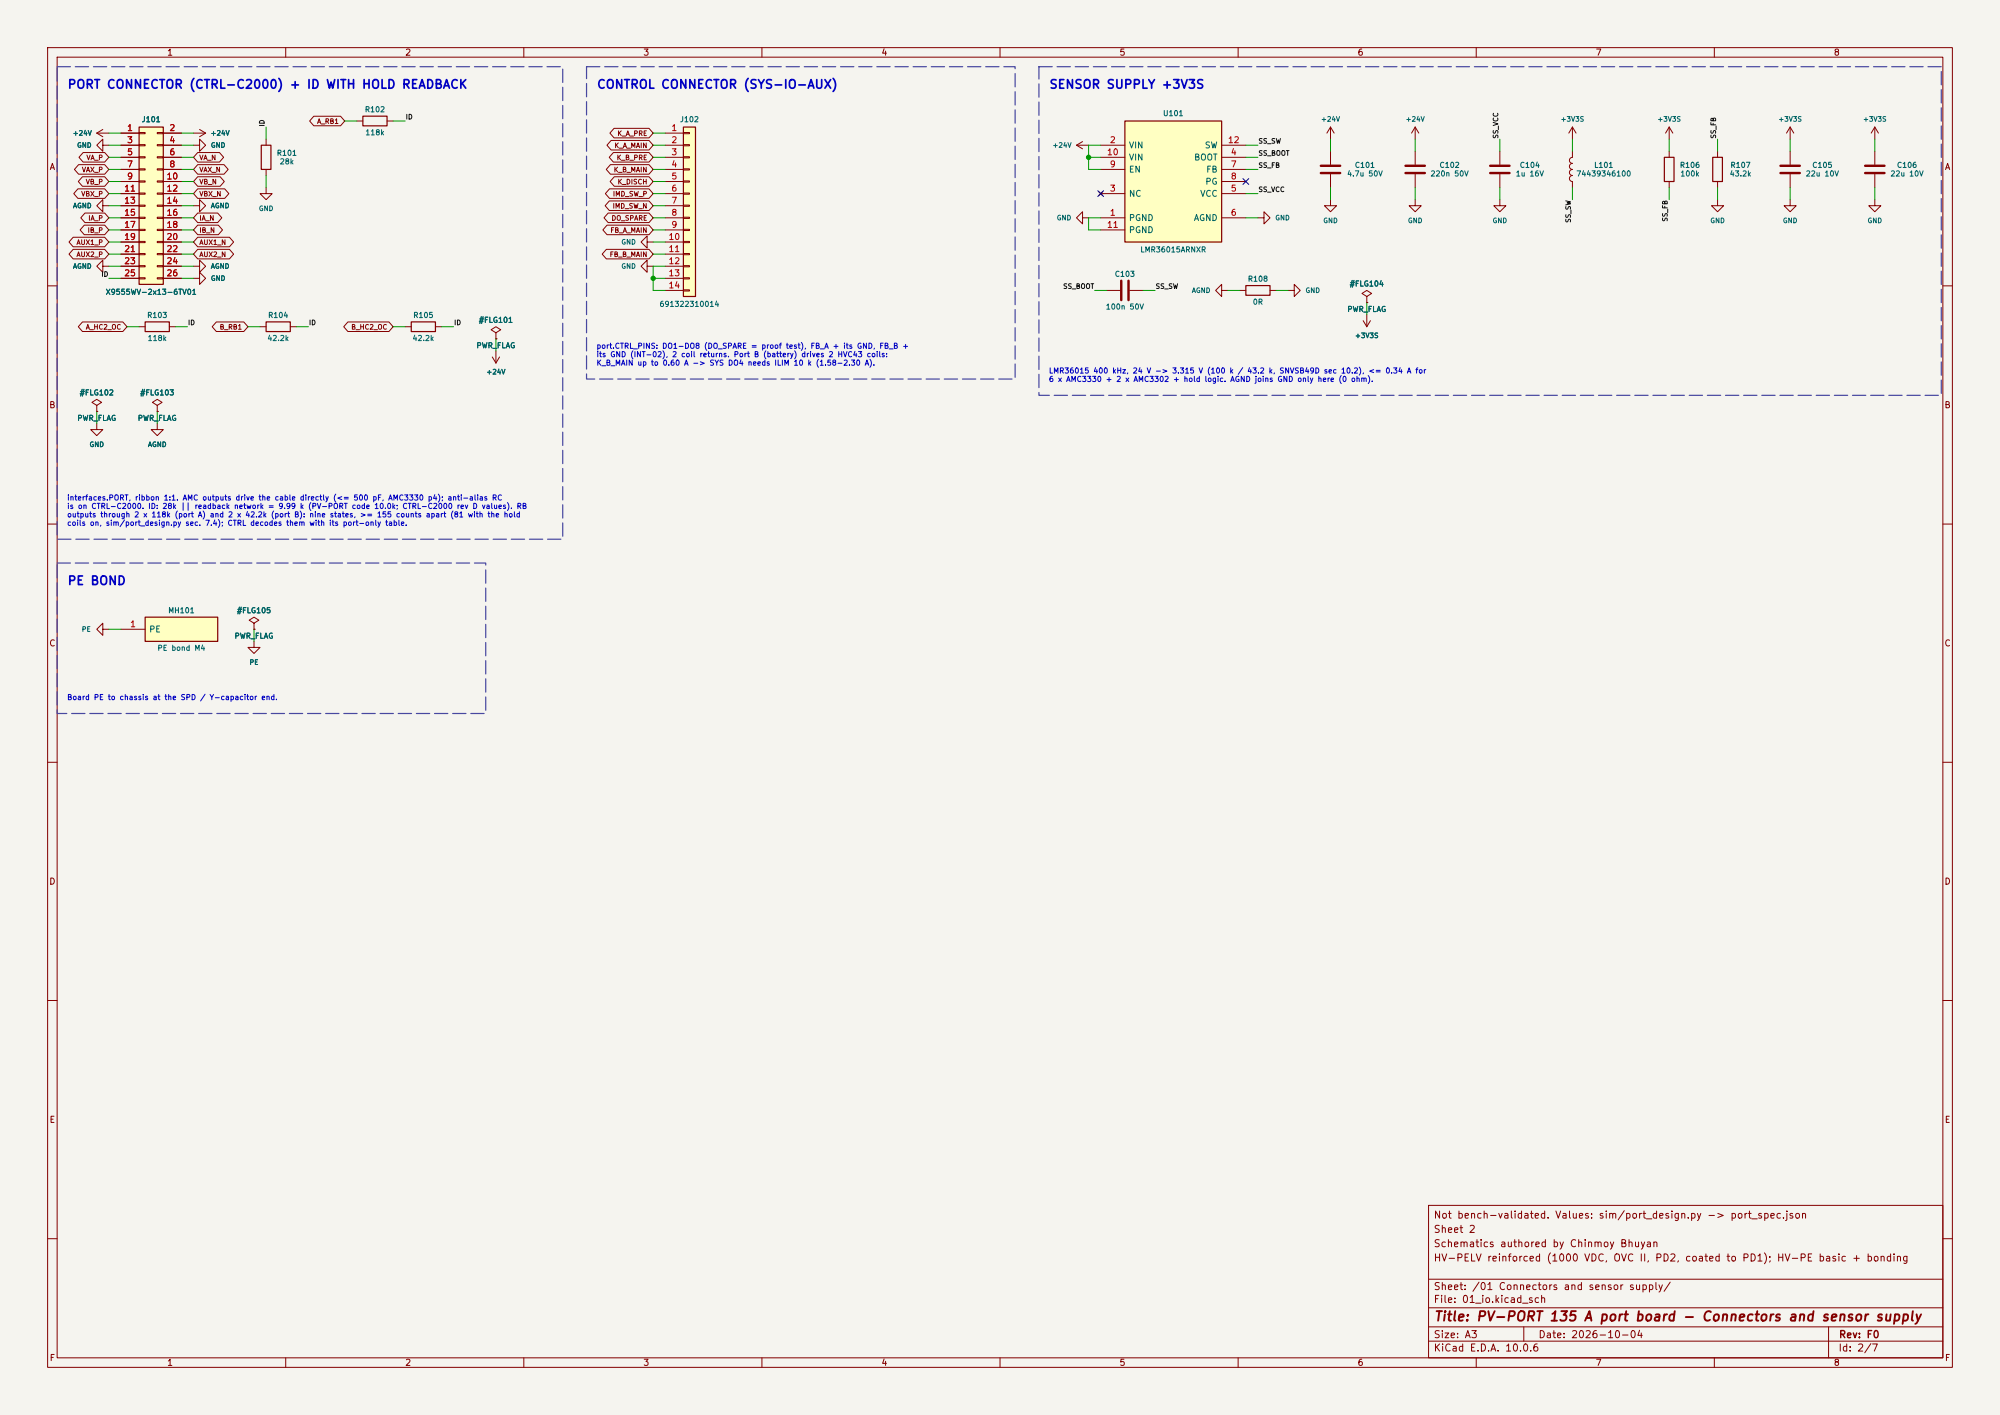
[picture p174: page 2]

PORT CONNECTOR (CTRL-C2000) + ID WITH HOLD READBACK

its GND (INT-02), 2 coil returns. Port B (battery) drives 2 HVC43 coils: K_B_MAIN up to 0.60 A -> SYS DO4 needs ILIM 10 k (1.58-2.30 A).

LMR36015 400 kHz, 24 V -> 3.315 V (100 k / 43.2 k, SNVSB49D sec 10.2), <= 0.34 A for 6 x AMC3330 + 2 x AMC3302 + hold logic. AGND joins GND only here (0 ohm).

interfaces.PORT, ribbon 1:1. AMC outputs drive the cable directly (<= 500 pF, AMC3330 p4); anti-alias RC
is on CTRL-C2000. ID: 28k || readback network = 9.99 k (PV-PORT code 10.0k; CTRL-C2000 rev D values). RB
outputs through 2 x 118k (port A) and 2 x 42.2k (port B): nine states, >= 155 counts apart (81 with the hold

Board PE to chassis at the SPD / Y-capacitor end. PE #FLG105 PWR_FLAG

Not bench-validated. Values: sim/port_design.py -> port_spec.json
Sheet 2
Schematics authored by Chinmoy Bhuyan
HV-PELV reinforced (1000 VDC, OVC II, PD2, coated to PD1); HV-PE basic + bonding

Sheet: /01 Connectors and sensor supply/
File: 01_io.kicad_sch
Title: PV-PORT 135 A port board - Connectors and sensor supply

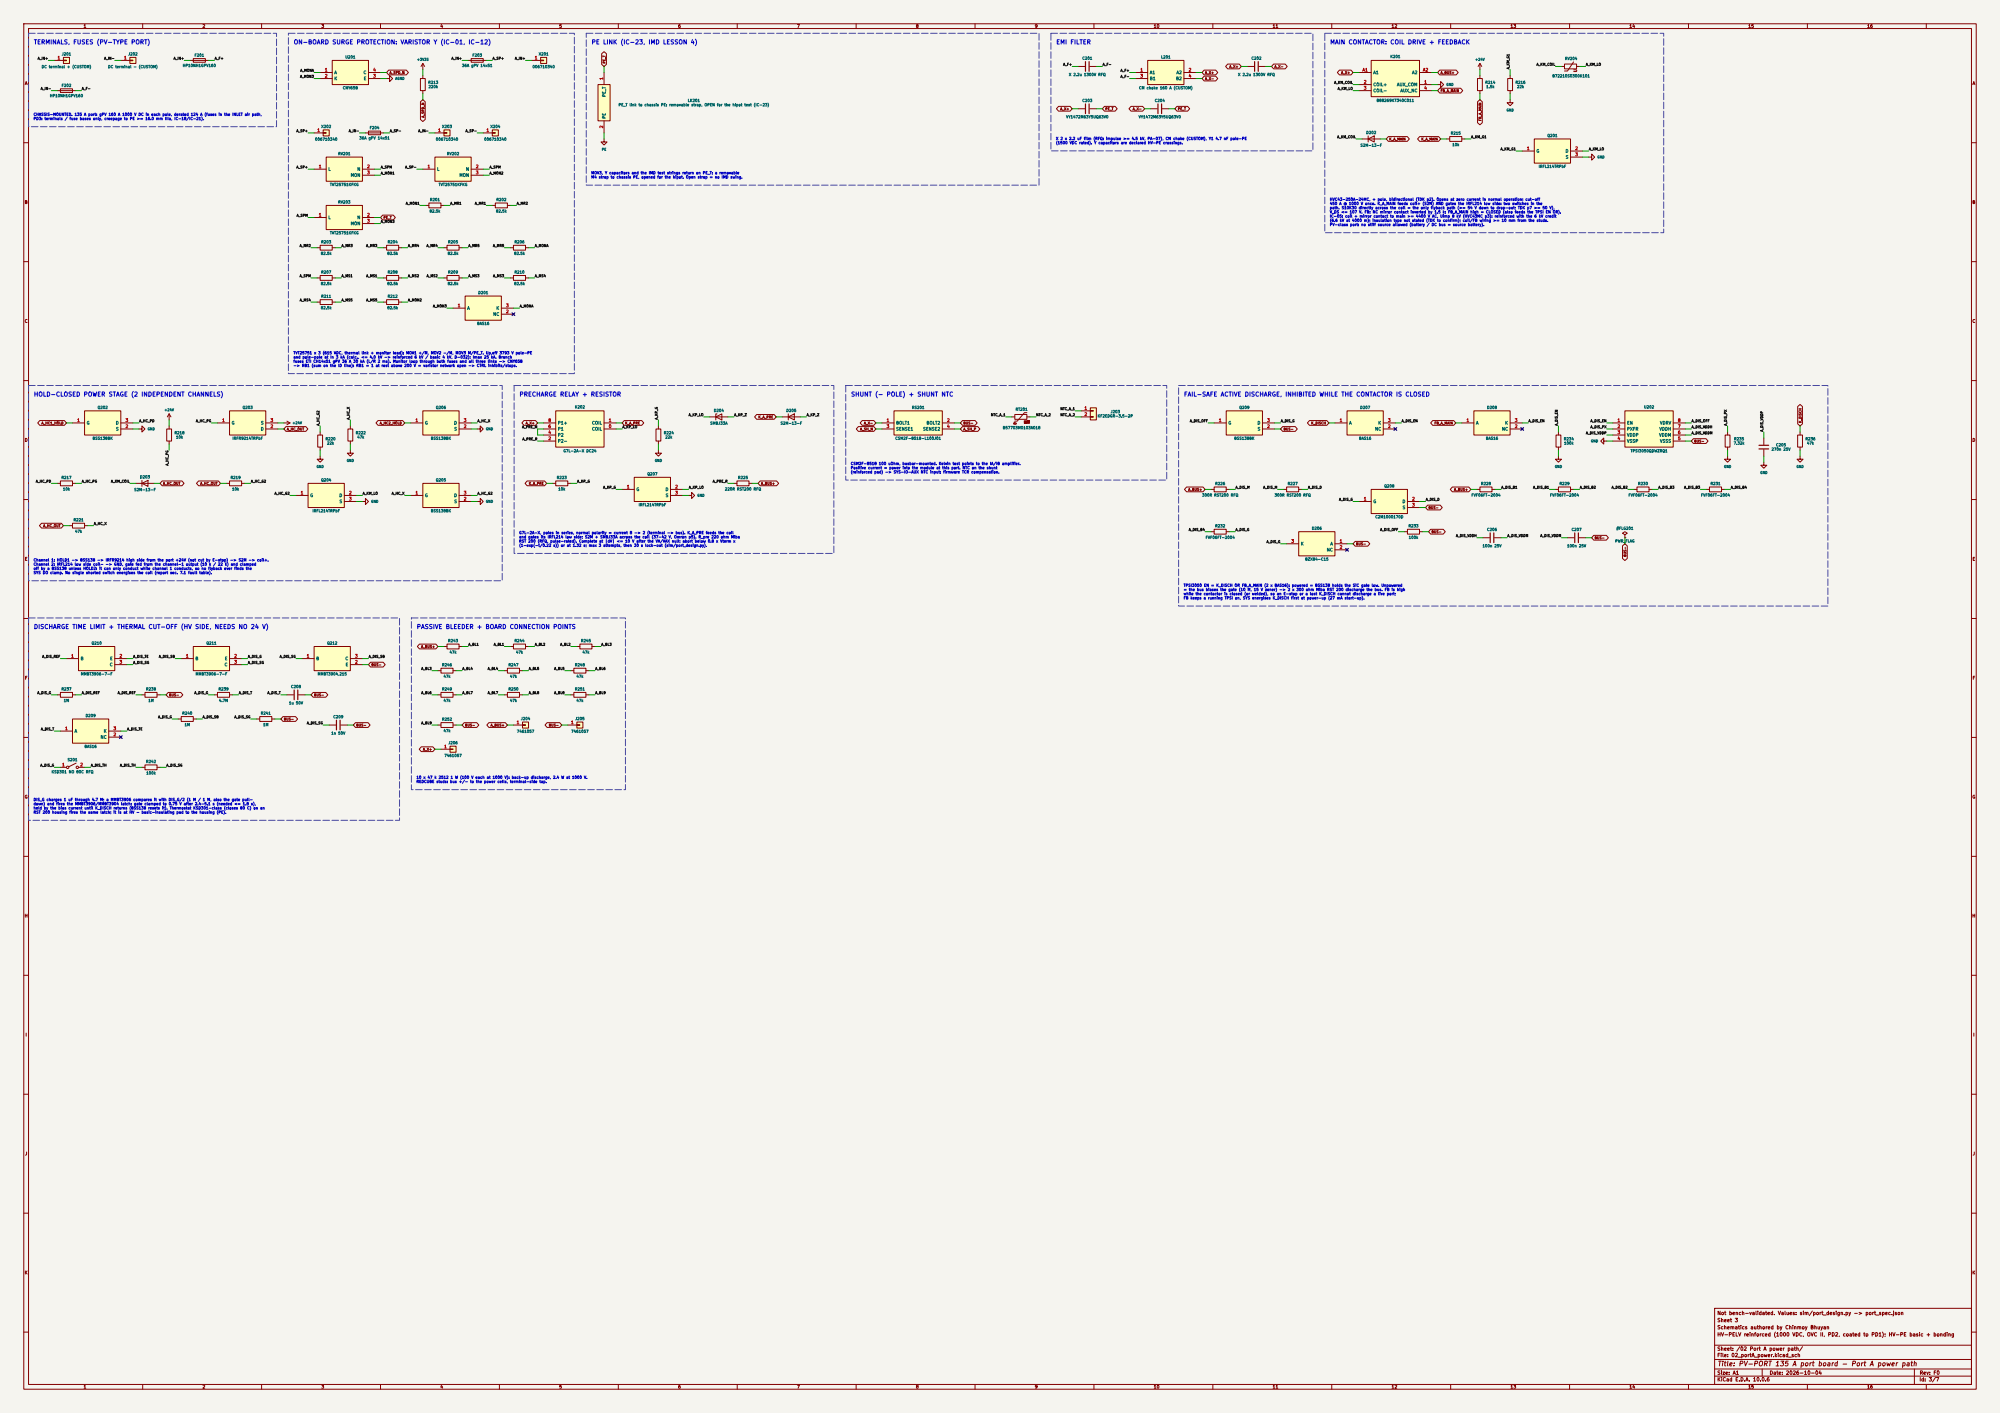
[picture p175: page 3]

PE LINK (IC-23, IMD LESSON 4) MOV3, Y capacitors and the IMD test strings return on PE_T: a removable M4 strap to chassis PE, opened for the hipot. Open strap = no IMD swing.

MAIN CONTACTOR: COIL DRIVE + FEEDBACK

LK201 PE_T link to chassis PE: removable strap, OPEN for the hipot test (IC-23)

(1500 VDC rated). Y capacitors are declared HV-PE crossings. CHASSIS-MOUNTED. 135 A port: gPV 160 A 1000 V DC in each pole, derated 124 A (fuses in the INLET air path, PD3: terminals / fuse bases only, creepage to PE >= 16.0 mm IIIa, IC-18/IC-21).

X 2 x 2.2 uF film (RFQ: impulse >= 4.5 kV, PA-07), CM choke (CUSTOM), Y1 4.7 nF pole-PE

HVC43-250A-24MC, + pole, bidirectional (TDK p2). Opens at zero current in normal operation; cut-off 450 A @ 1000 V once. K_A_MAIN feeds coil+ (S2M) AND gates the IRFL214 low side: two switches in the path. S10K30 directly across the coil = the only flyback path (>= 54 V down to drop-out; TDK p7 >= 50 V), V_DS <= 107 V. FB: NC mirror contact inverted by 1.5 k: FB_A_MAIN high = CLOSED (also feeds the TPSI EN OR).

IC-05: coil + mirror contact to main >= 4400 V AC, Uimp 8 kV (HVC43MC p3): reinforced with the 6 kV credit (6.6 kV at 4000 m); insulation type not stated (TDK to confirm); coil/FB wiring >= 10 mm from the studs. PV-class port: no stiff source allowed (battery / DC bus = source battery).

TVT25751 x 3 (615 VDC, thermal link + monitor lead): MOV1 +/M, MOV2 -/M, MOV3 M/PE_T. Up,eff 3793 V pole-PE
and pole-pole at In 3 kA (calc., <= 4.0 kV -> reinforced 6 kV / basic 4 kV, D-032); Imax 25 kA. Branch
fuses ETI CH14x51 gPV 36 A 30 kA (L/R 2 ms). Monitor loop through both fuses and all three links -> CNY65B -> RB1 (sum on the ID line): RB1 = 1 at rest above 200 V = varistor network open -> CTRL inhibits/stops.

CSM2F-8518 100 uOhm, busbar-mounted. Kelvin test points to the IA/IB amplifier. Positive current = power into the module at this port. NTC on the shunt (reinforced pad) -> SYS-IO-AUX NTC input: firmware TCR compensation.

G7L-2A-X, poles in series, normal polarity = current 8 -> 2 (terminal -> bus). K_A_PRE feeds the coil and gates its IRFL214 low side; S2M + SMBJ33A across the coil (37-42 V, Omron p5). R_pre 220 ohm Miba RST 200 (RFQ, pulse-rated). Complete at |dV| <= 10 V after the VA/VAX null; abort below 0.8 x Vterm x

(1-exp(-t/0.22 s)) or at 1.32 s; max 3 attempts, then 30 s lock-out (sim/port_design.py).

Channel 1: HOLD1 -> BSS138 -> IRFR9214 high side from the port +24V (not cut by E-stop) -> S2M -> coil+. Channel 2: IRFL214 low side coil- -> GND, gate fed from the channel-1 output (10 k / 22 k) and clamped

off by a BSS138 unless HOLD2: it can only conduct while channel 1 conducts, so no flyback ever finds the SYS DO clamp. No single shorted switch energises the coil (report sec. 7.1 fault table).

TPSI3050 EN = K_DISCH OR FB_A_MAIN (2 x BAS16): powered = BSS138 holds the SiC gate low. Unpowered = the bus biases the gate (10 M, 15 V zener) -> 2 x 300 ohm Miba RST 200 discharge the bus. FB is high while the contactor is closed (or welded), so an E-stop or a lost K_DISCH cannot discharge a live port; FB keeps a running TPSI on, SYS energises K_DISCH first at power-up (27 mA start-up).

DISCHARGE TIME LIMIT + THERMAL CUT-OFF (HV SIDE, NEEDS NO 24 V)

PASSIVE BLEEDER + BOARD CONNECTION POINTS

10 x 47 k 2512 1 W (100 V each at 1000 V): back-up discharge, 2.4 W at 1000 V. REDCUBE studs: bus +/- to the power cells, terminal-side tap.

DIS_G charges 1 uF through 4.7 M; a MMBT3906 compares it with DIS_G/2 (1 M / 1 M, also the gate pull-
down) and fires the MMBT3906/MMBT3904 latch: gate clamped to 0.75 V after 2.4-5.1 s (needed <= 1.8 s), held by the bias current until K_DISCH returns (BSS138 resets it). Thermostat KSD301-class (closes 80 C) on an RST 200 housing fires the same latch; it is at HV - basic-insulating pad to the housing (PE).

Not bench-validated. Values: sim/port_design.py -> port_spec.json
Sheet 3
Schematics authored by Chinmoy Bhuyan
HV-PELV reinforced (1000 VDC, OVC II, PD2, coated to PD1); HV-PE basic + bonding

Sheet: /02 Port A power path/
File: 02_portA_power.kicad_sch
Title: PV-PORT 135 A port board - Port A power path

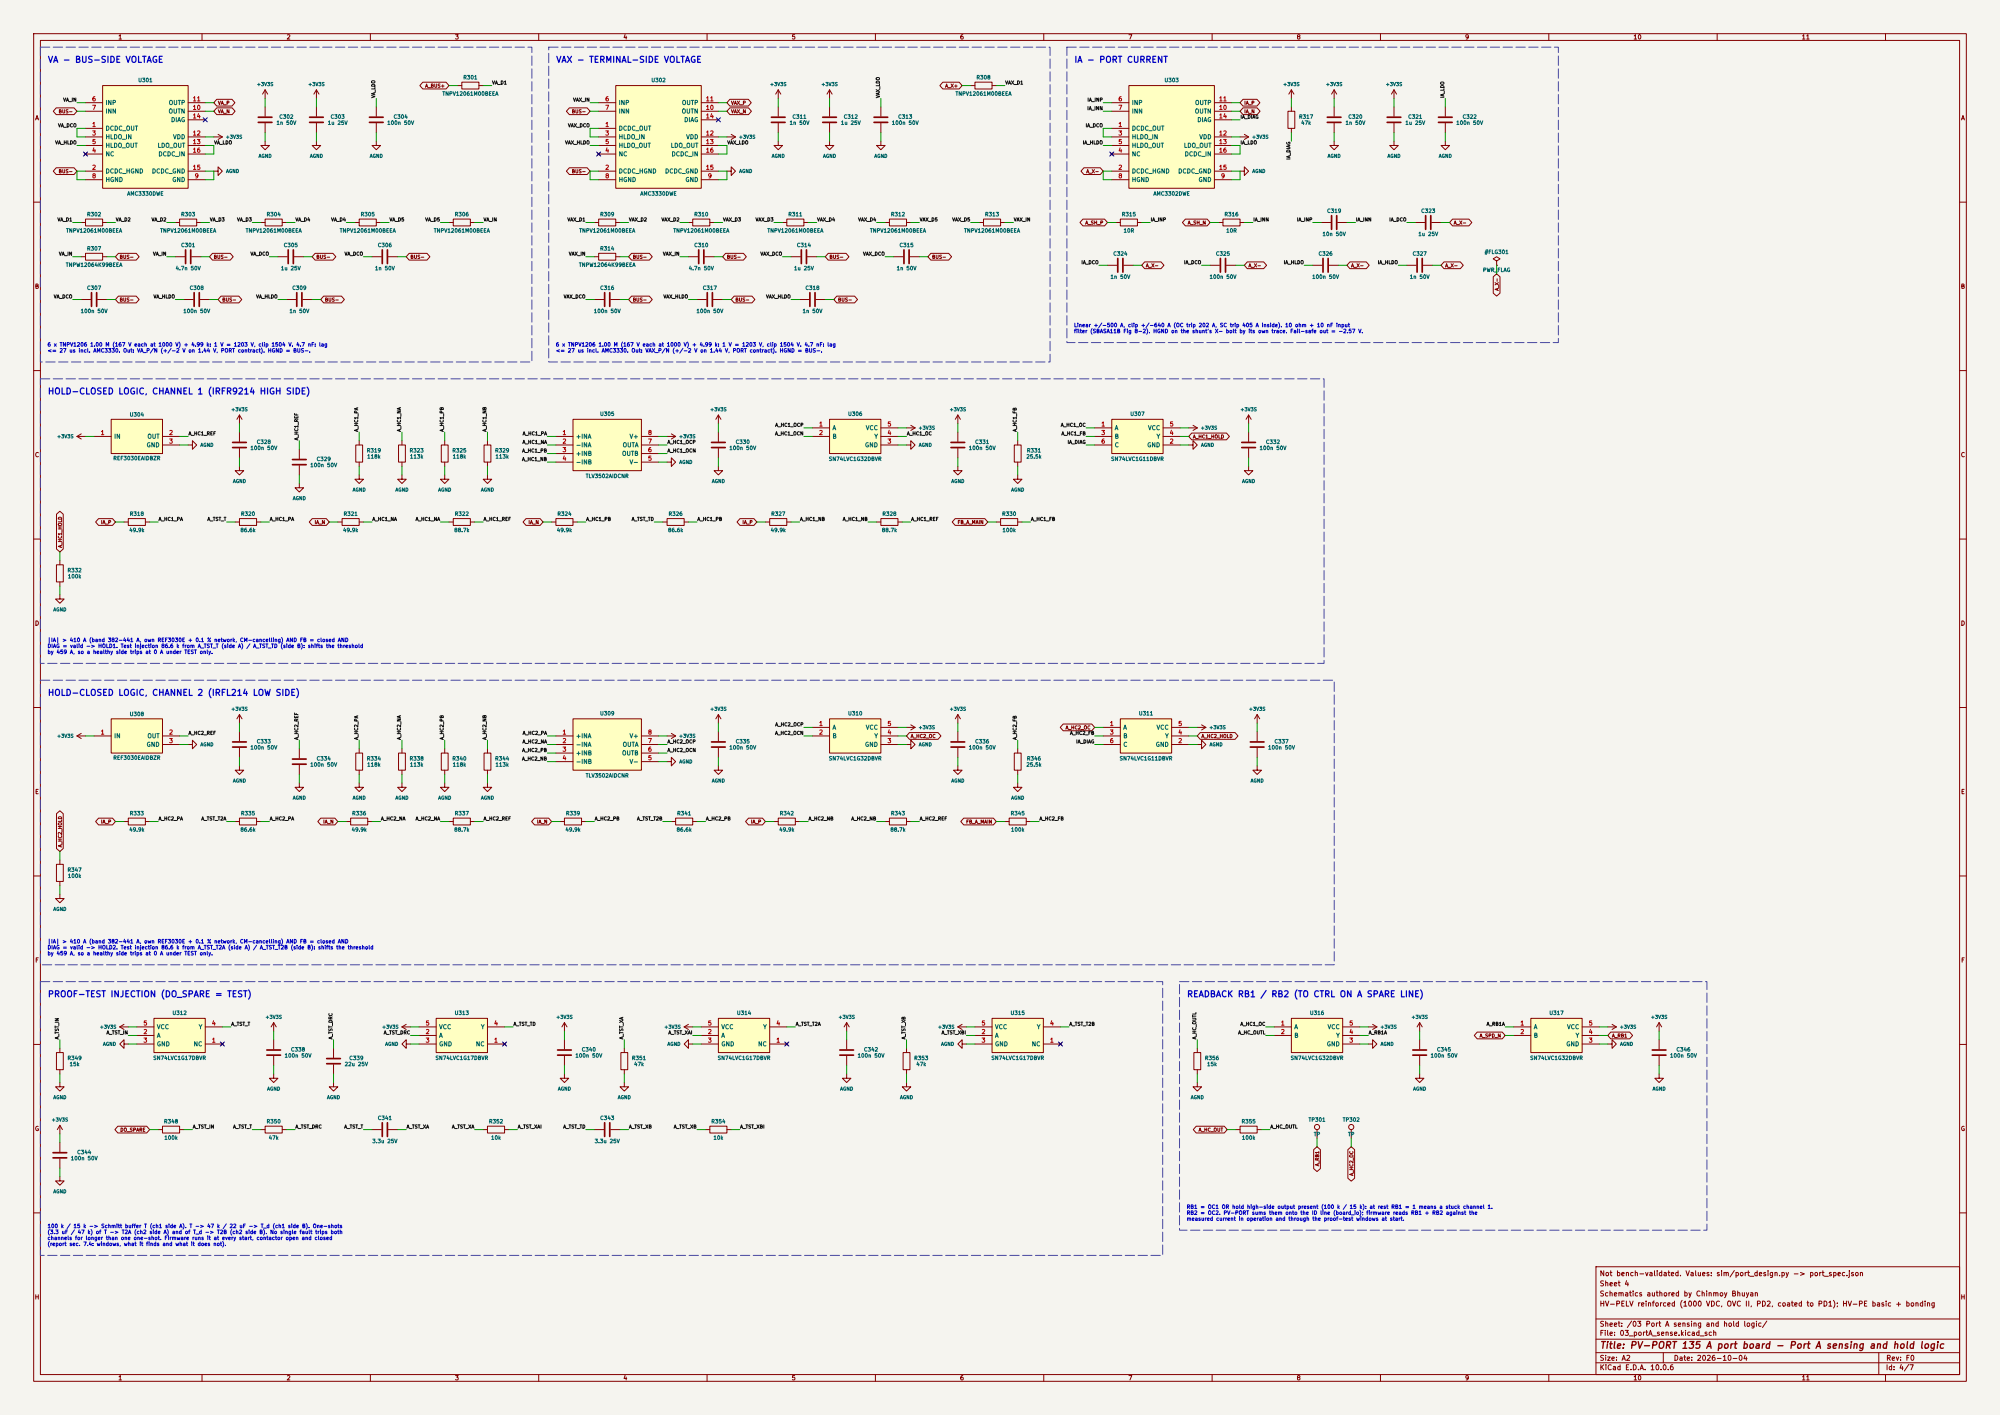
[picture p176: page 4]

VA - BUS-SIDE VOLTAGE

6 x TNPV1206 1.00 M (167 V each at 1000 V) + 4.99 k: 1 V = 1203 V, clip 1504 V. 4.7 nF: lag <= 27 us incl. AMC3330. Out: VAX_P/N (+/-2 V on 1.44 V, PORT contract). HGND = BUS-. VAX - TERMINAL-SIDE VOLTAGE

Linear +/-500 A, clip +/-640 A (OC trip 202 A, SC trip 405 A inside). 10 ohm + 10 nF input
filter (SBASA11B Fig 8-2). HGND on the shunt's X- bolt by its own trace. Fail-safe out = -2.57 V.

6 x TNPV1206 1.00 M (167 V each at 1000 V) + 4.99 k: 1 V = 1203 V, clip 1504 V. 4.7 nF: lag <= 27 us incl. AMC3330. Out: VA_P/N (+/-2 V on 1.44 V, PORT contract). HGND = BUS-. HOLD-CLOSED LOGIC, CHANNEL 1 (IRFR9214 HIGH SIDE)

A_HC1_OCN PROOF-TEST INJECTION (DO_SPARE = TEST)

IA| > 410 A (band 382-441 A, own REF3030E + 0.1 % network, CM-cancelling) AND FB = closed AND
DIAG = valid -> HOLD1. Test injection 86.6 k from A_TST_T (side A) / A_TST_TD (side B): shifts the threshold
by 459 A, so a healthy side trips at 0 A under TEST only.

HOLD-CLOSED LOGIC, CHANNEL 2 (IRFL214 LOW SIDE)

DIAG = valid -> HOLD2. Test injection 86.6 k from A_TST_T2A (side A) / A_TST_T2B (side B): shifts the threshold
by 459 A, so a healthy side trips at 0 A under TEST only. 100 k / 15 k -> Schmitt buffer T (ch1 side A). T -> 47 k / 22 uF -> T_d (ch1 side B). One-shots
FGH

READBACK RB1 / RB2 (TO CTRL ON A SPARE LINE)

(3.3 uF / 47 k) of T -> T2A (ch2 side A) and of T_d -> T2B (ch2 side B). No single fault trips both
channels for longer than one one-shot. Firmware runs it at every start, contactor open and closed

Not bench-validated. Values: sim/port_design.py -> port_spec.json
Sheet 4

Sheet: /03 Port A sensing and hold logic/
File: 03_portA_sense.kicad_sch
Title: PV-PORT 135 A port board - Port A sensing and hold logic

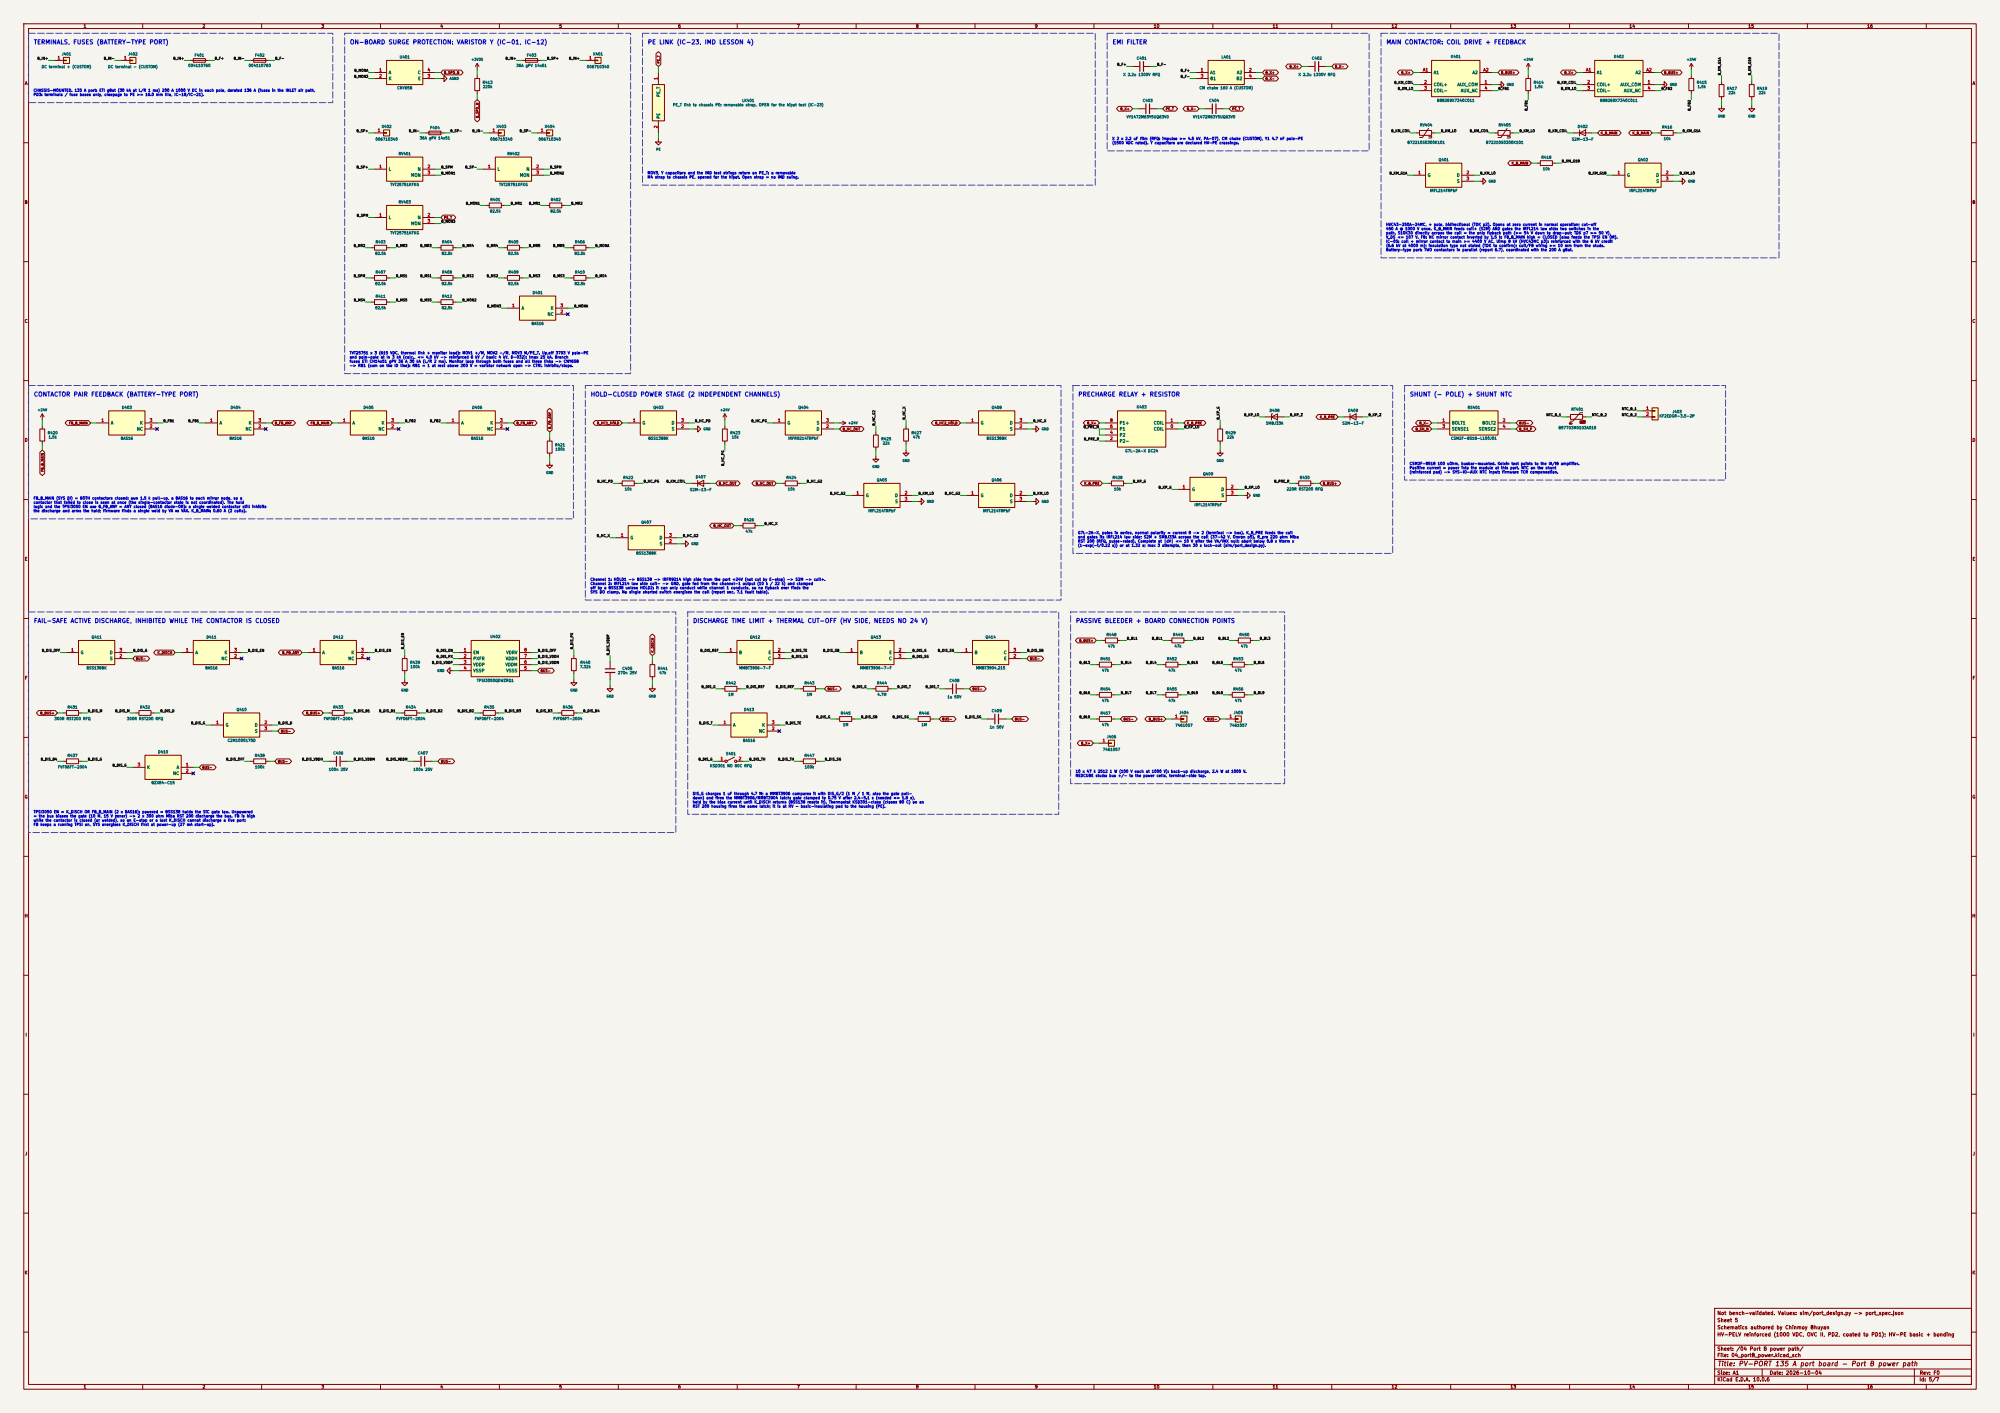
[picture p177: page 5]

TERMINALS, FUSES (BATTERY-TYPE PORT)

ON-BOARD SURGE PROTECTION: VARISTOR Y (IC-01, IC-12)

MOV3, Y capacitors and the IMD test strings return on PE_T: a removable M4 strap to chassis PE, opened for the hipot. Open strap = no IMD swing. CHASSIS-MOUNTED. 135 A port: ETI gBat (30 kA at L/R 1 ms) 200 A 1000 V DC in each pole, derated 136 A (fuses in the INLET air path, PD3: terminals / fuse bases only, creepage to PE >= 16.0 mm IIIa, IC-18/IC-21).

LK401 PE_T link to chassis PE: removable strap, OPEN for the hipot test (IC-23) PE

X 2 x 2.2 uF film (RFQ: impulse >= 4.5 kV, PA-07), CM choke (CUSTOM), Y1 4.7 nF pole-PE
(1500 VDC rated). Y capacitors are declared HV-PE crossings.

HVC43-250A-24MC, + pole, bidirectional (TDK p2). Opens at zero current in normal operation; cut-off 450 A @ 1000 V once. K_B_MAIN feeds coil+ (S2M) AND gates the IRFL214 low side: two switches in the path. S10K30 directly across the coil = the only flyback path (>= 54 V down to drop-out; TDK p7 >= 50 V), V_DS <= 107 V. FB: NC mirror contact inverted by 1.5 k: FB_B_MAIN high = CLOSED (also feeds the TPSI EN OR).

IC-05: coil + mirror contact to main >= 4400 V AC, Uimp 8 kV (HVC43MC p3): reinforced with the 6 kV credit (6.6 kV at 4000 m); insulation type not stated (TDK to confirm); coil/FB wiring >= 10 mm from the studs. Battery-type port: TWO contactors in parallel (report 6.7), coordinated with the 200 A gBat.

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

HOLD-CLOSED POWER STAGE (2 INDEPENDENT CHANNELS)
Q403 BSS138BK G
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
