vectivolt/PCM/hardware/PV-PWR-4/outputs/PV-PWR-4_schematic.pdf

1 | 2 | 3 | 4 | 5 | 6 | 7 | 8

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
# Title: PV-PWR-4 power board - Cover / Hierarchy

Size: A3 | through the BC817 follower; foldback detector on the live winding | Rev: A2
KiCad | E.D.A. 10.0.6 | Id: 1/26 | F Date: 2026-10-05

## File: PV-PWR-4.kicad_sch

## Sheet: /

Live board referenced to BUS-; gate islands functional; SELV winding reinforced; HV-PE basic

## Schematics authored by Chinmoy Bhuyan

## Sheet 1
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
