vectivolt/PCM/hardware/AUX-HV/sheets/01_input.kicad_sch

## KiCad design hardware/AUX-HV/sheets/01_input.kicad_sch (2026-10-04)

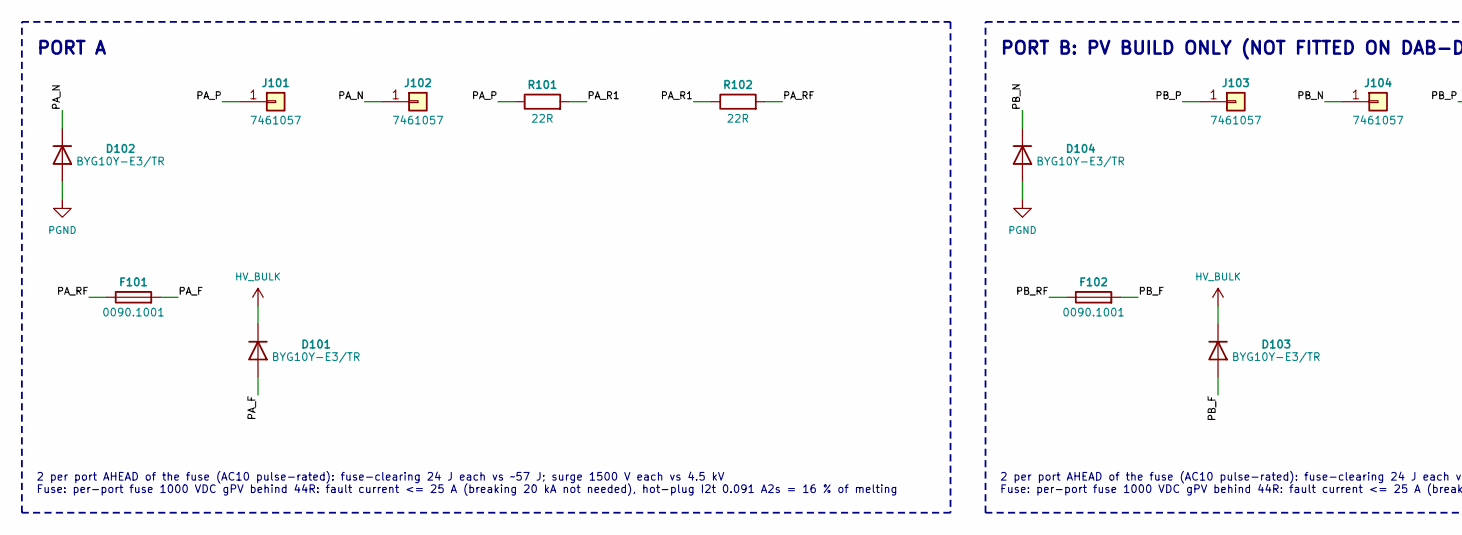
[picture p178: schematic 01_input.kicad_sch, part in row 1, column 1]

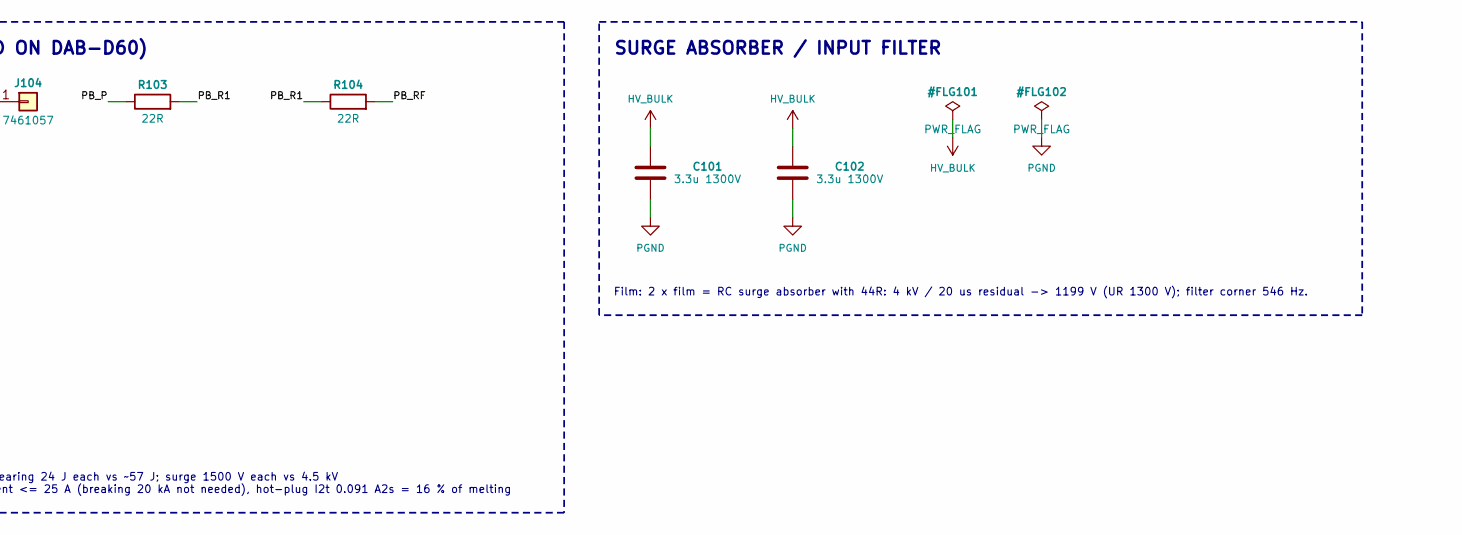
[picture p179: schematic 01_input.kicad_sch, part in row 1, column 2]

Parts:
C101, C102: 3.3u 1300V; MPN FCSA3DS335K050ID90BE3
D101, D102, D103, D104: BYG10Y-E3/TR; MPN BYG10Y-E3/TR
F101, F102: 0090.1001; MPN 0090.1001
J101, J102, J103, J104: 7461057; MPN 7461057
R101, R102, R103, R104: 22R; MPN AC10000002209JAB00

Connections:
HV_BULK: C101.1, C102.1, D101.1 (K), D103.1 (K)
PA_F: D101.2 (A), F101.2
PA_N: D102.1 (K), J102.1
PA_P: J101.1, R101.1
PA_R1: R101.2, R102.1
PA_RF: F101.1, R102.2
PB_F: D103.2 (A), F102.2
PB_N: D104.1 (K), J104.1
PB_P: J103.1, R103.1
PB_R1: R103.2, R104.1
PB_RF: F102.1, R104.2
PGND: C101.2, C102.2, D102.2 (A), D104.2 (A)

Notes on the sheet:
SURGE ABSORBER / INPUT FILTER
2 per port AHEAD of the fuse (AC10 pulse-rated): fuse-clearing 24 J each vs ~57 J; surge 1500 V each vs 4.5 kV Fuse: per-port fuse 1000 VDC gPV behind 44R: fault current <= 25 A (breaking 20 kA not needed), hot-plug I2t 0.091 A2s = 16 % of melting
Film: 2 x film = RC surge absorber with 44R: 4 kV / 20 us residual -> 1199 V (UR 1300 V); filter corner 546 Hz.
PORT B: PV BUILD ONLY (NOT FITTED ON DAB-D60)
PORT A
