vectivolt/PCM/hardware/AUX-HV/sheets/02_startup.kicad_sch

## KiCad design hardware/AUX-HV/sheets/02_startup.kicad_sch (2026-10-04)

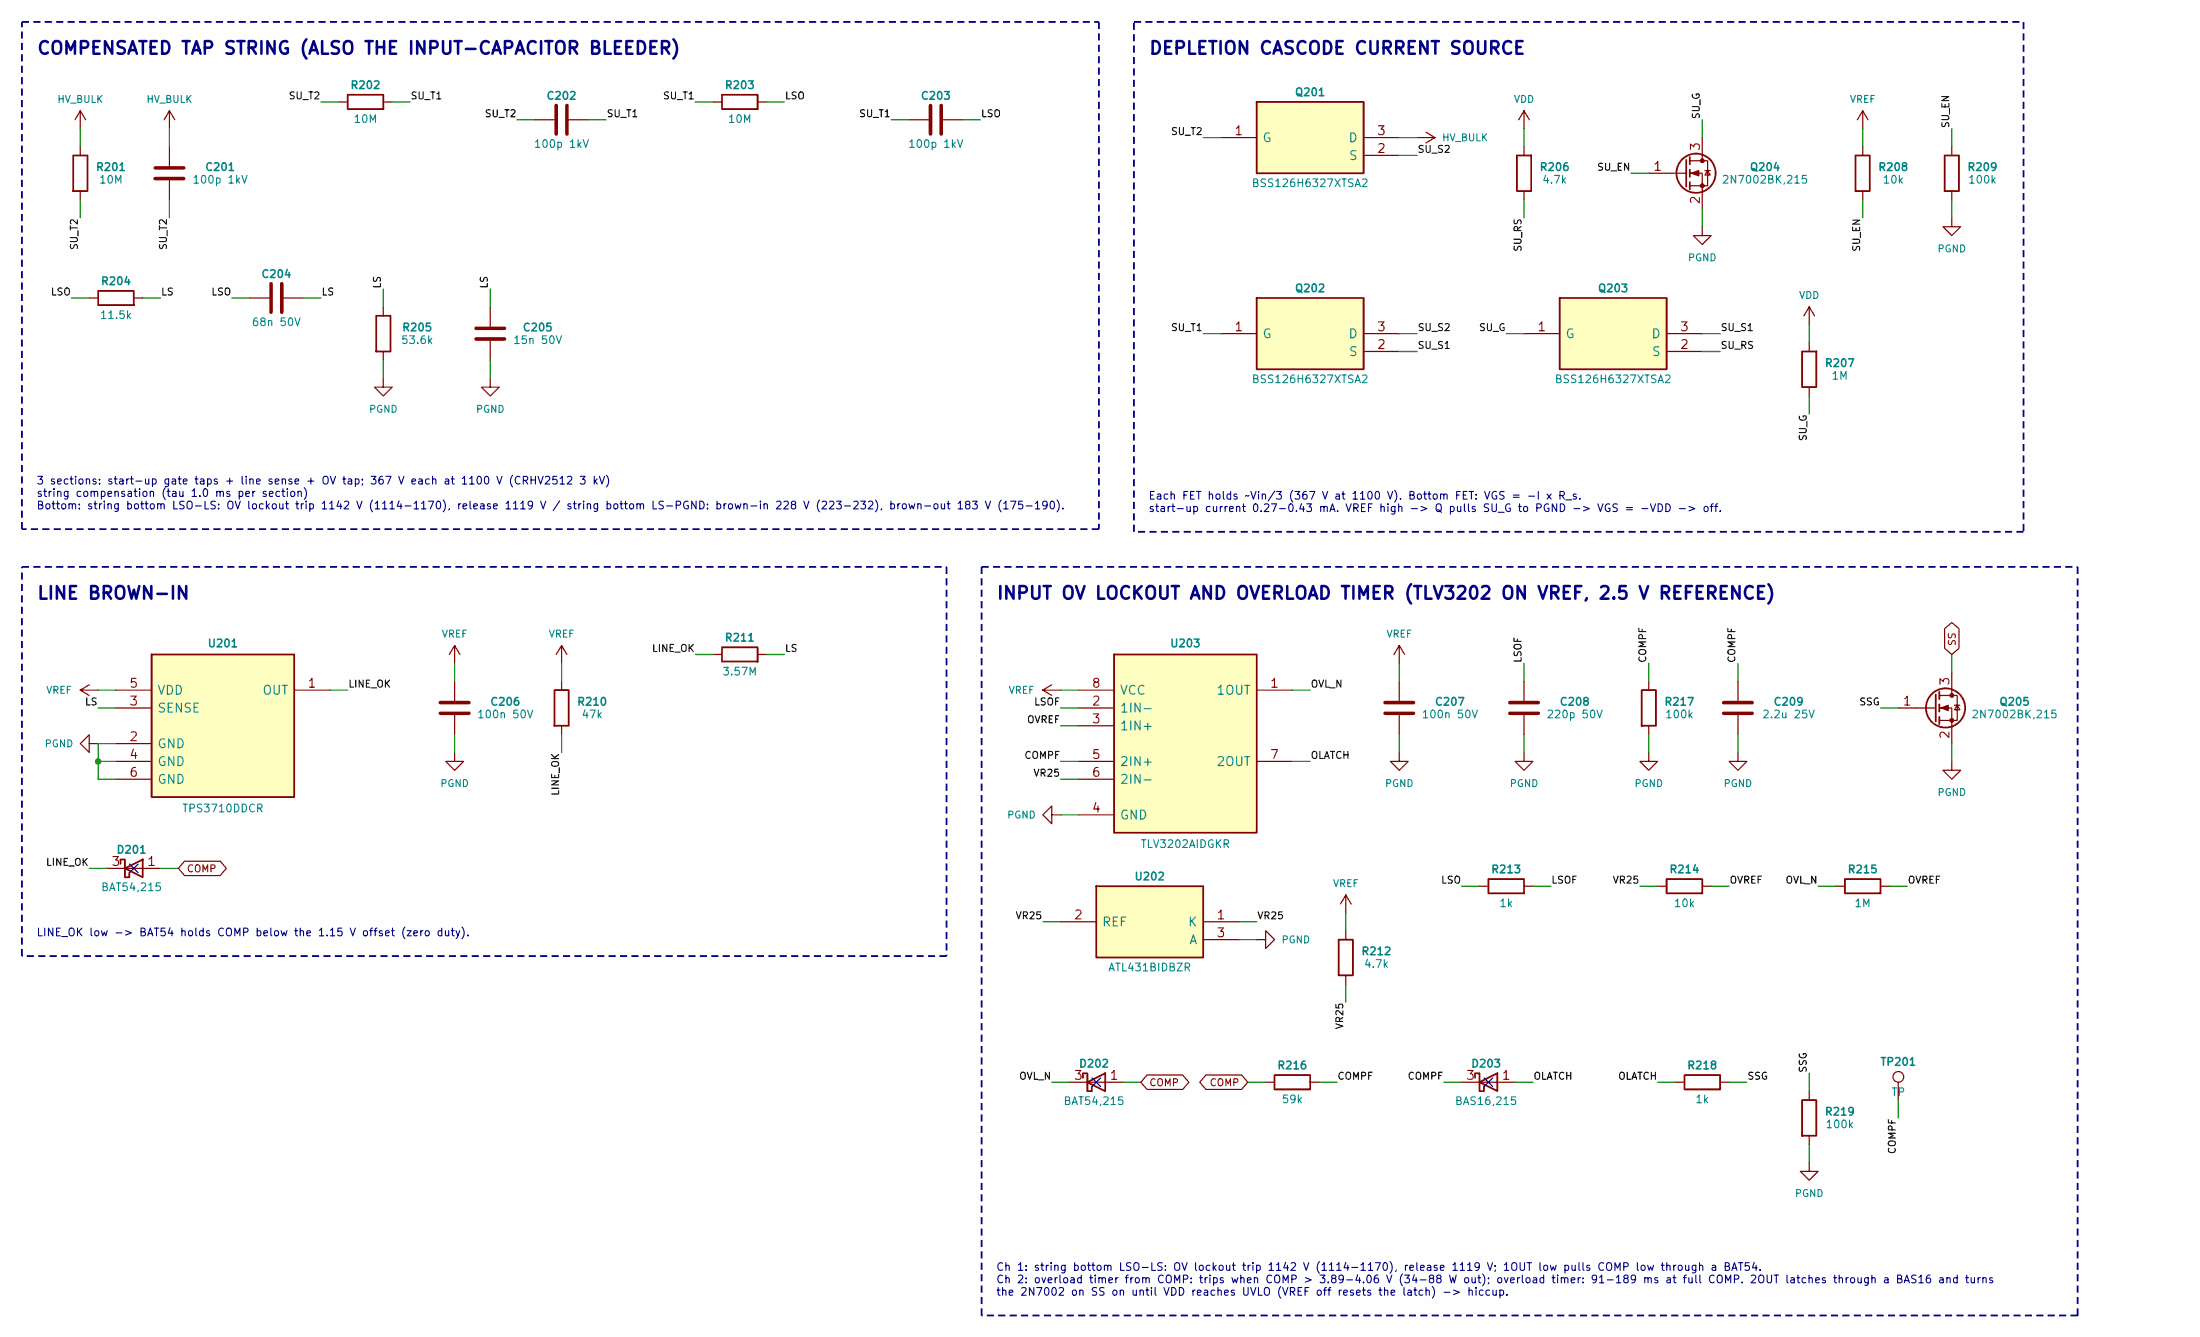
[picture p180: schematic 02_startup.kicad_sch]

Parts:
C201, C202, C203: 100p 1kV
C204: 68n 50V
C205: 15n 50V
C206, C207: 100n 50V
C208: 220p 50V
C209: 2.2u 25V
D201, D202: BAT54,215; MPN BAT54,215
D203: BAS16,215; MPN BAS16,215
Q201, Q202, Q203: BSS126H6327XTSA2; MPN BSS126H6327XTSA2
Q204, Q205: 2N7002BK,215; MPN 2N7002BK,215
R201, R202, R203: 10M; MPN CRHV2512AF10M0FKFB
R204: 11.5k
R205: 53.6k
R206, R212: 4.7k
R207, R215: 1M
R208, R214: 10k
R209, R217, R219: 100k
R210: 47k
R211: 3.57M
R213, R218: 1k
R216: 59k
TP201: TP
U201: TPS3710DDCR; MPN TPS3710DDCR
U202: ATL431BIDBZR; MPN ATL431BIDBZR
U203: TLV3202AIDGKR; MPN TLV3202AIDGKR

Connections:
COMP: D201.1 (A), D202.1 (A), R216.1
COMPF: C209.1, D203.3 (K), R216.2, R217.1, TP201.1, U203.5 (2IN+)
HV_BULK: C201.1, Q201.3 (D), R201.1
LINE_OK: D201.3 (K), R210.2, R211.1, U201.1 (OUT)
LS: C204.2, C205.1, R204.2, R205.1, R211.2, U201.3 (SENSE)
LSO: C203.2, C204.1, R203.2, R204.1, R213.1
LSOF: C208.1, R213.2, U203.2 (1IN-)
OLATCH: D203.1 (A), R218.1, U203.7 (2OUT)
OVL_N: D202.3 (K), R215.1, U203.1 (1OUT)
OVREF: R214.2, R215.2, U203.3 (1IN+)
PGND: C205.2, C206.2, C207.2, C208.2, C209.2, Q204.2 (S), Q205.2 (S), R205.2, R209.2, R217.2, R219.2, U201.2 (GND), U201.4 (GND), U201.6 (GND), U202.3 (A), U203.4 (GND)
SS: Q205.3 (D)
SSG: Q205.1 (G), R218.2, R219.1
SU_EN: Q204.1 (G), R208.2, R209.1
SU_G: Q203.1 (G), Q204.3 (D), R207.1
SU_RS: Q203.2 (S), R206.1
SU_S1: Q202.2 (S), Q203.3 (D)
SU_S2: Q201.2 (S), Q202.3 (D)
SU_T1: C202.2, C203.1, Q202.1 (G), R202.2, R203.1
SU_T2: C201.2, C202.1, Q201.1 (G), R201.2, R202.1
VDD: R206.2, R207.2
VR25: R212.2, R214.1, U202.1 (K), U202.2 (REF), U203.6 (2IN-)
VREF: C206.1, C207.1, R208.1, R210.1, R212.1, U201.5 (VDD), U203.8 (VCC)

Notes on the sheet:
DEPLETION CASCODE CURRENT SOURCE
INPUT OV LOCKOUT AND OVERLOAD TIMER (TLV3202 ON VREF, 2.5 V REFERENCE)
Ch 1: string bottom LSO-LS: OV lockout trip 1142 V (1114-1170), release 1119 V; 1OUT low pulls COMP low through a BAT54. Ch 2: overload timer from COMP: trips when COMP > 3.89-4.06 V (34-88 W out); overload timer: 91-189 ms at full COMP. 2OUT latches through a BAS16 and turns the 2N7002 on SS on un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
Each FET holds ~Vin/3 (367 V at 1100 V). Bottom FET: VGS = -I x R_s. start-up current 0.27-0.43 mA. VREF high -> Q pulls SU_G to PGND -> VGS = -VDD -> off.
LINE_OK low -> BAT54 holds COMP below the 1.15 V offset (zero duty).
LINE BROWN-IN
COMPENSATED TAP STRING (ALSO THE INPUT-CAPACITOR BLEEDER)
3 sections: start-up gate taps + line sense + OV tap; 367 V each at 1100 V (CRHV2512 3 kV) string compensation (tau 1.0 ms per section) Bottom: string bottom LSO-LS: OV lockout trip 1142 V (1114-1170), release 1119 V / string bottom LS-PGND: brown-in 228 V (223-232), brown-out 183 V (175-190).
