vectivolt/PCM/hardware/AUX-HV/sheets/03_power.kicad_sch

## KiCad design hardware/AUX-HV/sheets/03_power.kicad_sch (2026-10-04)

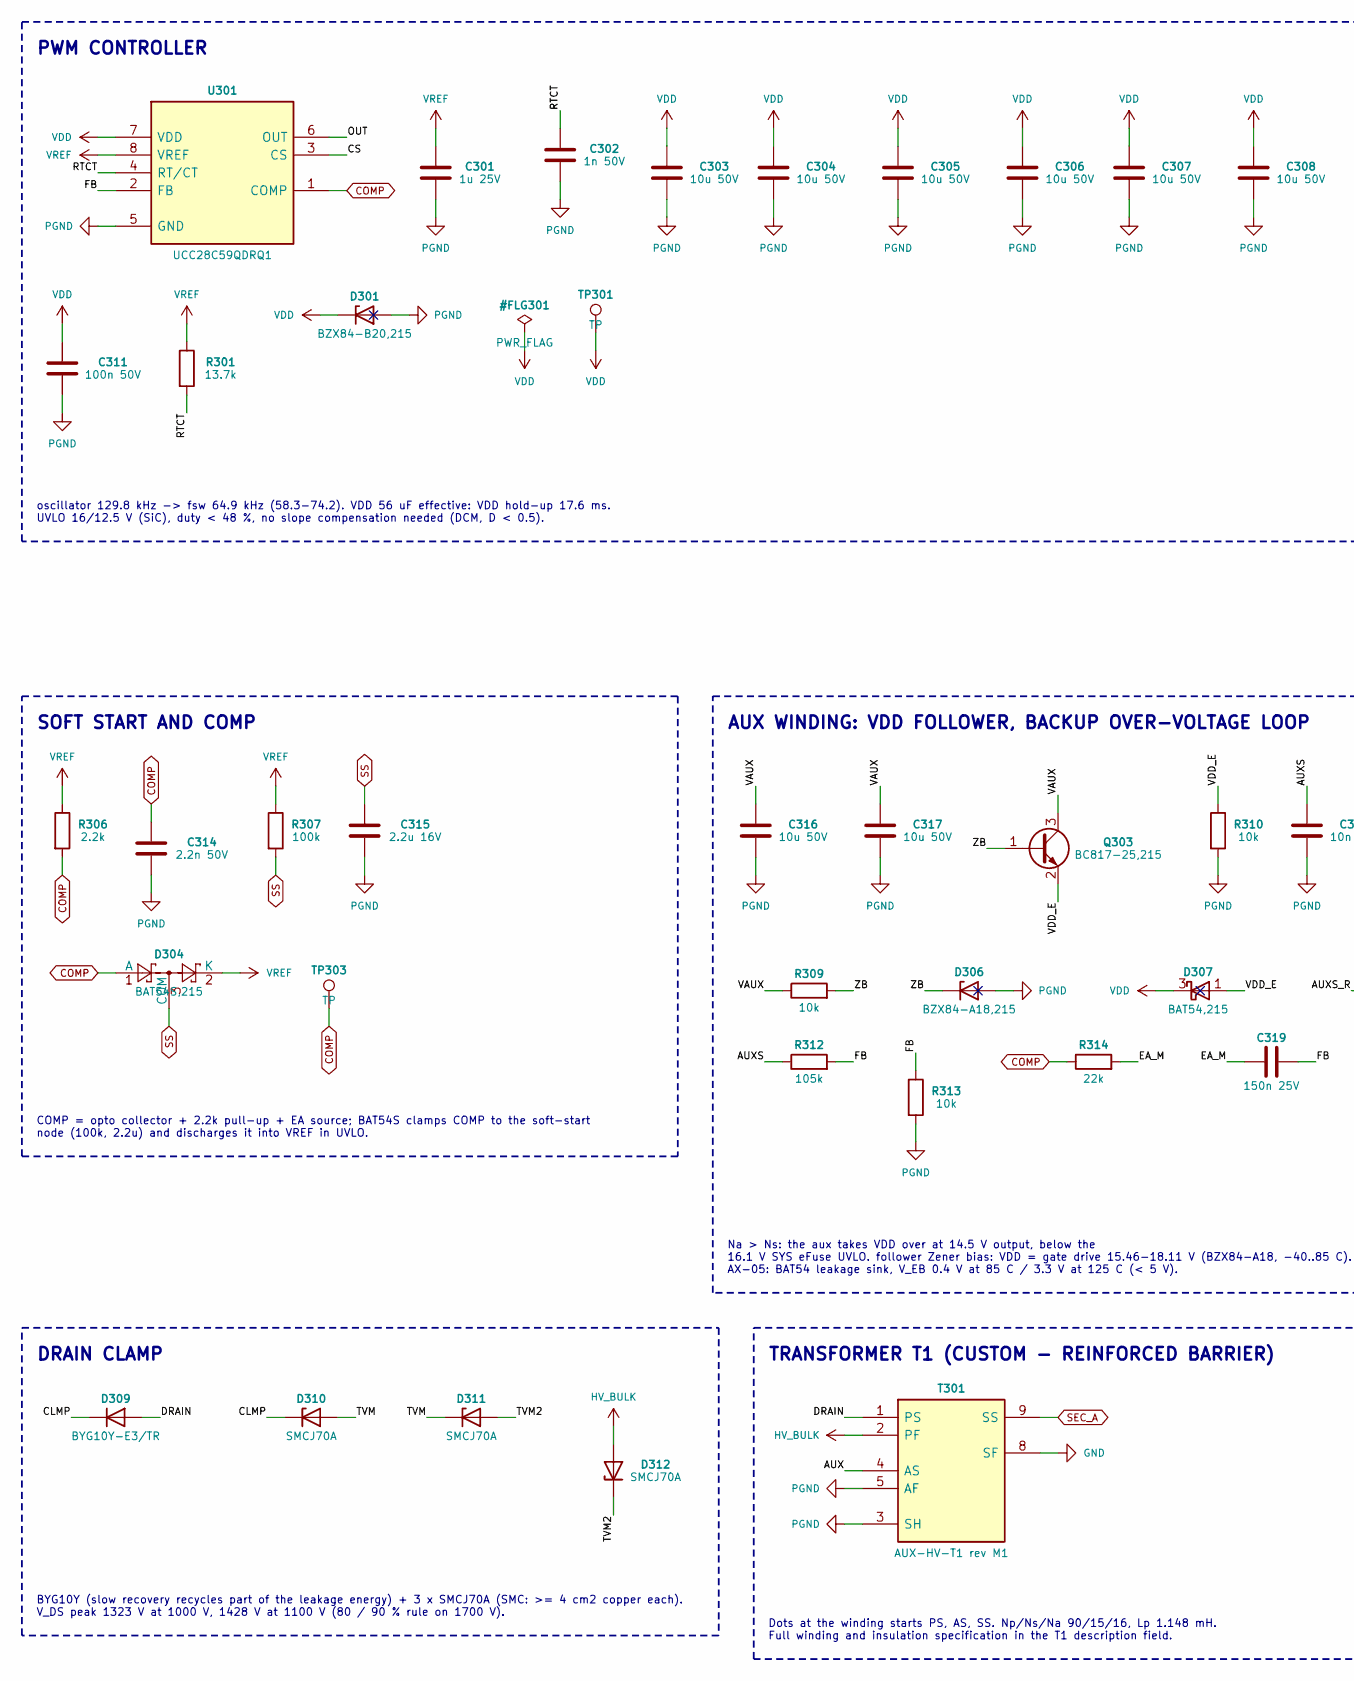
[picture p181: schematic 03_power.kicad_sch, part in row 1, column 1]

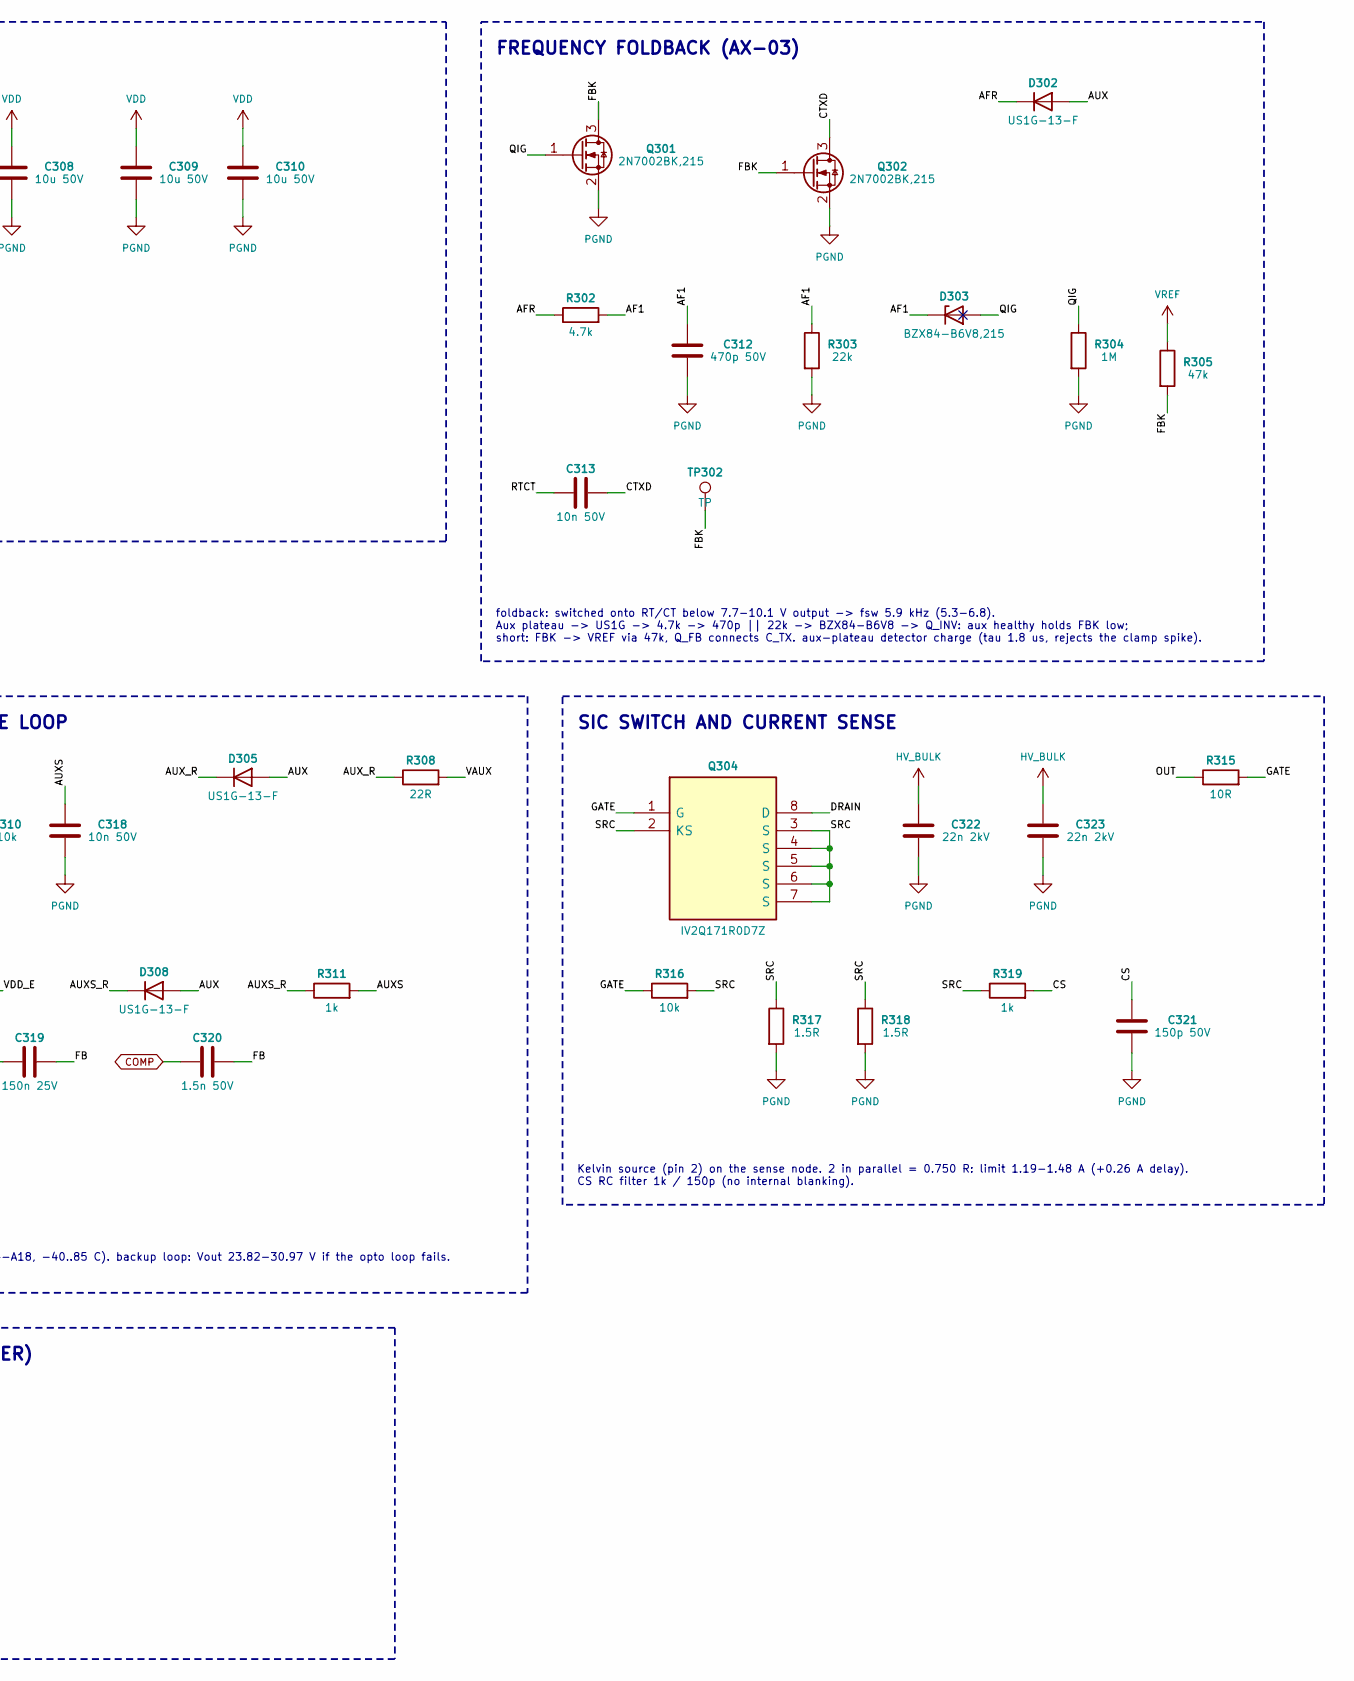
[picture p182: schematic 03_power.kicad_sch, part in row 1, column 2]

Parts:
C301: 1u 25V
C302: 1n 50V
C303, C304, C305, C306, C307, C308, C309, C310, C316, C317: 10u 50V
C311: 100n 50V
C312: 470p 50V
C313, C318: 10n 50V
C314: 2.2n 50V
C315: 2.2u 16V
C319: 150n 25V
C320: 1.5n 50V
C321: 150p 50V
C322, C323: 22n 2kV
D301: BZX84-B20,215; MPN BZX84-B20,215
D302, D305, D308: US1G-13-F; MPN US1G-13-F
D303: BZX84-B6V8,215; MPN BZX84-B6V8,215
D304: BAT54S,215; MPN BAT54S,215
D306: BZX84-A18,215; MPN BZX84-A18,215
D307: BAT54,215; MPN BAT54,215
D309: BYG10Y-E3/TR; MPN BYG10Y-E3/TR
D310, D311, D312: SMCJ70A; MPN SMCJ70A
Q301, Q302: 2N7002BK,215; MPN 2N7002BK,215
Q303: BC817-25,215; MPN BC817-25,215
Q304: IV2Q171R0D7Z; MPN IV2Q171R0D7Z
R301: 13.7k
R302: 4.7k
R303, R314: 22k
R304: 1M
R305: 47k
R306: 2.2k
R307: 100k
R308: 22R
R309, R310, R313, R316: 10k
R311, R319: 1k
R312: 105k
R315: 10R
R317, R318: 1.5R
T301: AUX-HV-T1 rev M1; MPN AUX-HV-T1 rev M1
TP301, TP302, TP303: TP
U301: UCC28C59QDRQ1; MPN UCC28C59QDRQ1

Connections:
AF1: C312.1, D303.3 (K), R302.2, R303.1
AFR: D302.1 (K), R302.1
AUX: D302.2 (A), D305.2 (A), D308.2 (A), T301.4 (AS)
AUXS: C318.1, R311.2, R312.1
AUXS_R: D308.1 (K), R311.1
AUX_R: D305.1 (K), R308.1
CLMP: D309.1 (K), D310.1 (K)
COMP: C314.1, C320.1, D304.1 (A), R306.2, R314.1, TP303.1, U301.1 (COMP)
CS: C321.1, R319.2, U301.3 (CS)
CTXD: C313.2, Q302.3 (D)
DRAIN: D309.2 (A), Q304.8 (D), T301.1 (PS)
EA_M: C319.1, R314.2
FB: C319.2, C320.2, R312.2, R313.1, U301.2 (FB)
FBK: Q301.3 (D), Q302.1 (G), R305.2, TP302.1
GATE: Q304.1 (G), R315.2, R316.1
GND: T301.8 (SF)
HV_BULK: C322.1, C323.1, D312.2 (A), T301.2 (PF)
OUT: R315.1, U301.6 (OUT)
PGND: C301.2, C302.2, C303.2, C304.2, C305.2, C306.2, C307.2, C308.2, C309.2, C310.2, C311.2, C312.2, C314.2, C315.2, C316.2, C317.2, C318.2, C321.2, C322.2, C323.2, D301.1 (A), D306.1 (A), Q301.2 (S), Q302.2 (S), R303.2, R304.2, R310.2, R313.2, R317.2, R318.2, T301.3 (SH), T301.5 (AF), U301.5 (GND)
QIG: D303.1 (A), Q301.1 (G), R304.1
RTCT: C302.1, C313.1, R301.2, U301.4 (RT/CT)
SEC_A: T301.9 (SS)
SRC: Q304.2 (KS), Q304.3 (S), Q304.4 (S), Q304.5 (S), Q304.6 (S), Q304.7 (S), R316.2, R317.1, R318.1, R319.1
SS: C315.1, D304.3 (COM), R307.2
TVM: D310.2 (A), D311.1 (K)
TVM2: D311.2 (A), D312.1 (K)
VAUX: C316.1, C317.1, Q303.3 (C), R308.2, R309.1
VDD: C303.1, C304.1, C305.1, C306.1, C307.1, C308.1, C309.1, C310.1, C311.1, D301.3 (K), D307.3 (K), TP301.1, U301.7 (VDD)
VDD_E: D307.1 (A), Q303.2 (E), R310.1
VREF: C301.1, D304.2 (K), R301.1, R305.1, R306.1, R307.1, U301.8 (VREF)
ZB: D306.3 (K), Q303.1 (B), R309.2

Notes on the sheet:
SOFT START AND COMP
foldback: switched onto RT/CT below 7.7-10.1 V output -> fsw 5.9 kHz (5.3-6.8). Aux plateau -> US1G -> 4.7k -> 470p || 22k -> BZX84-B6V8 -> Q_INV: aux healthy holds FBK low; short: FBK -> VREF via 47k, Q_FB connects C_TX. aux-plateau detector charge (tau 1.8 us, rejects the clamp spike).
COMP = opto collector + 2.2k pull-up + EA source; BAT54S clamps COMP to the soft-start node (100k, 2.2u) and discharges it into VREF in UVLO.
SIC SWITCH AND CURRENT SENSE
Na > Ns: the aux takes VDD over at 14.5 V output, below the 16.1 V SYS eFuse UVLO. follower Zener bias: VDD = gate drive 15.46-18.11 V (BZX84-A18, -40..85 C). backup loop: Vout 23.82-30.97 V if the opto loop fails. AX-05: BAT54 leakage sink, V_EB 0.4 V at 85 C / 3.3 V at 125 C (< 5 V).
AUX WINDING: VDD FOLLOWER, BACKUP OVER-VOLTAGE LOOP
Dots at the winding starts PS, AS, SS. Np/Ns/Na 90/15/16, Lp 1.148 mH. Full winding and insulation specification in the T1 description field.
PWM CONTROLLER
Kelvin source (pin 2) on the sense node. 2 in parallel = 0.750 R: limit 1.19-1.48 A (+0.26 A delay). CS RC filter 1k / 150p (no internal blanking).
oscillator 129.8 kHz -> fsw 64.9 kHz (58.3-74.2). VDD 56 uF effective: VDD hold-up 17.6 ms. UVLO 16/12.5 V (SiC), duty < 48 %, no slope compensation needed (DCM, D < 0.5).
TRANSFORMER T1 (CUSTOM - REINFORCED BARRIER)
DRAIN CLAMP
FREQUENCY FOLDBACK (AX-03)
BYG10Y (slow recovery recycles part of the leakage energy) + 3 x SMCJ70A (SMC: >= 4 cm2 copper each). V_DS peak 1323 V at 1000 V, 1428 V at 1100 V (80 / 90 % rule on 1700 V).
