vectivolt/PCM/hardware/AUX-HV/sheets/04_secondary.kicad_sch

## KiCad design hardware/AUX-HV/sheets/04_secondary.kicad_sch (2026-10-04)

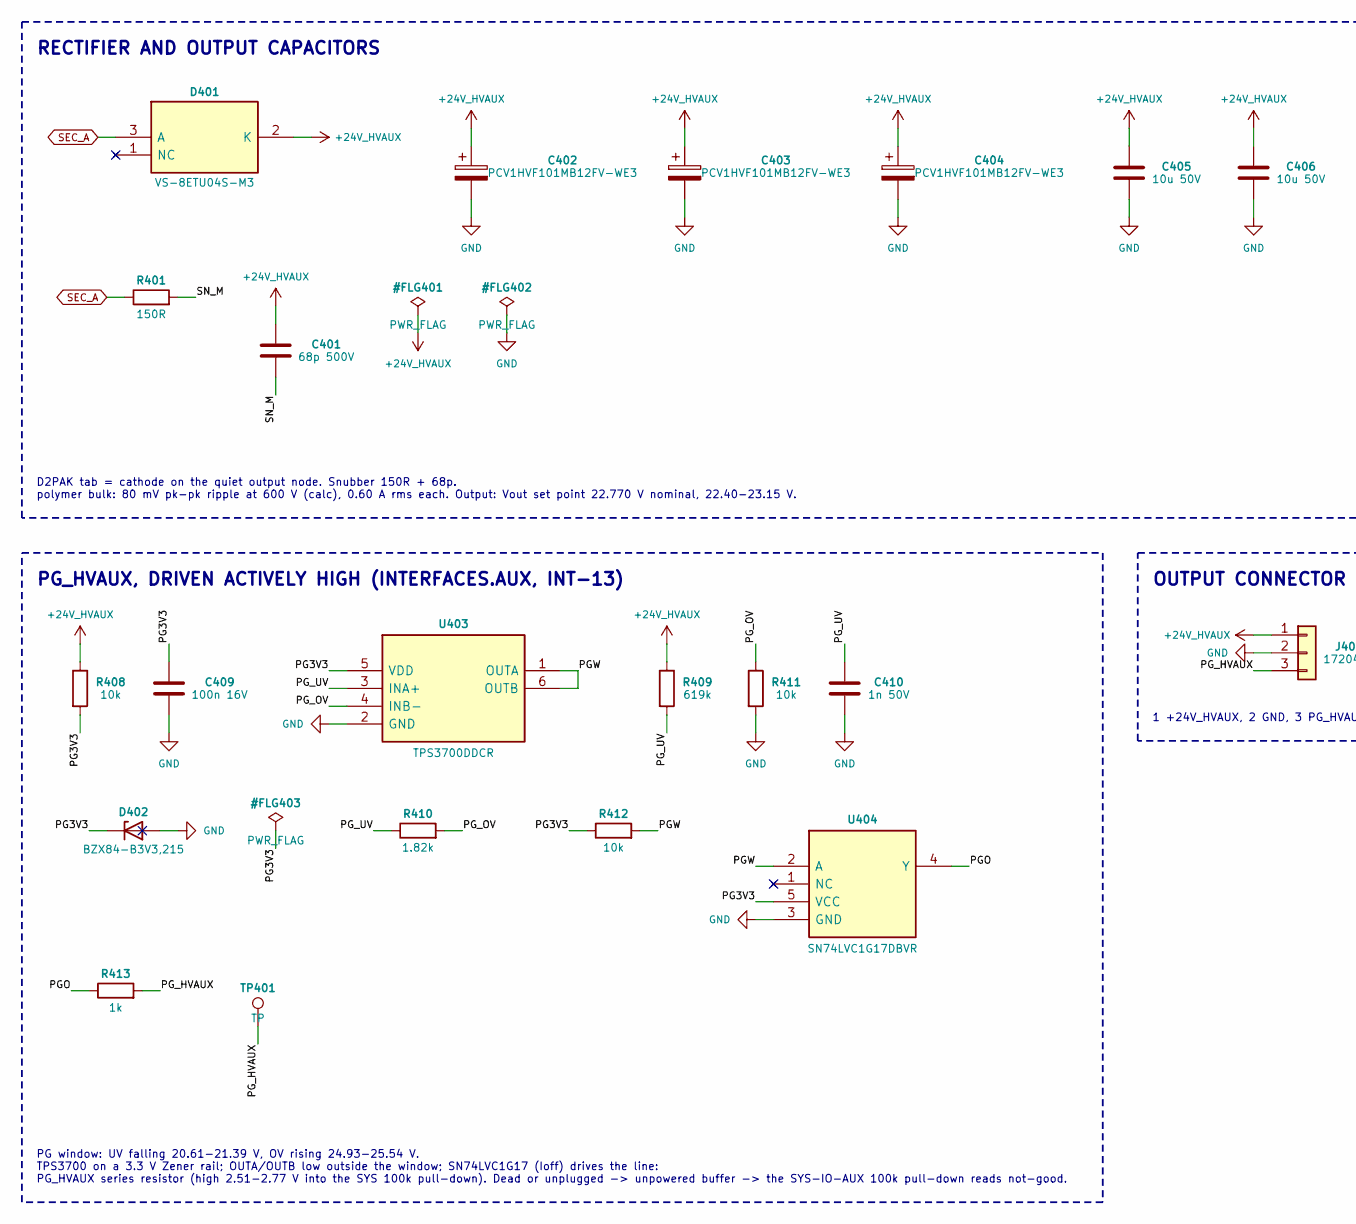
[picture p183: schematic 04_secondary.kicad_sch, part in row 1, column 1]

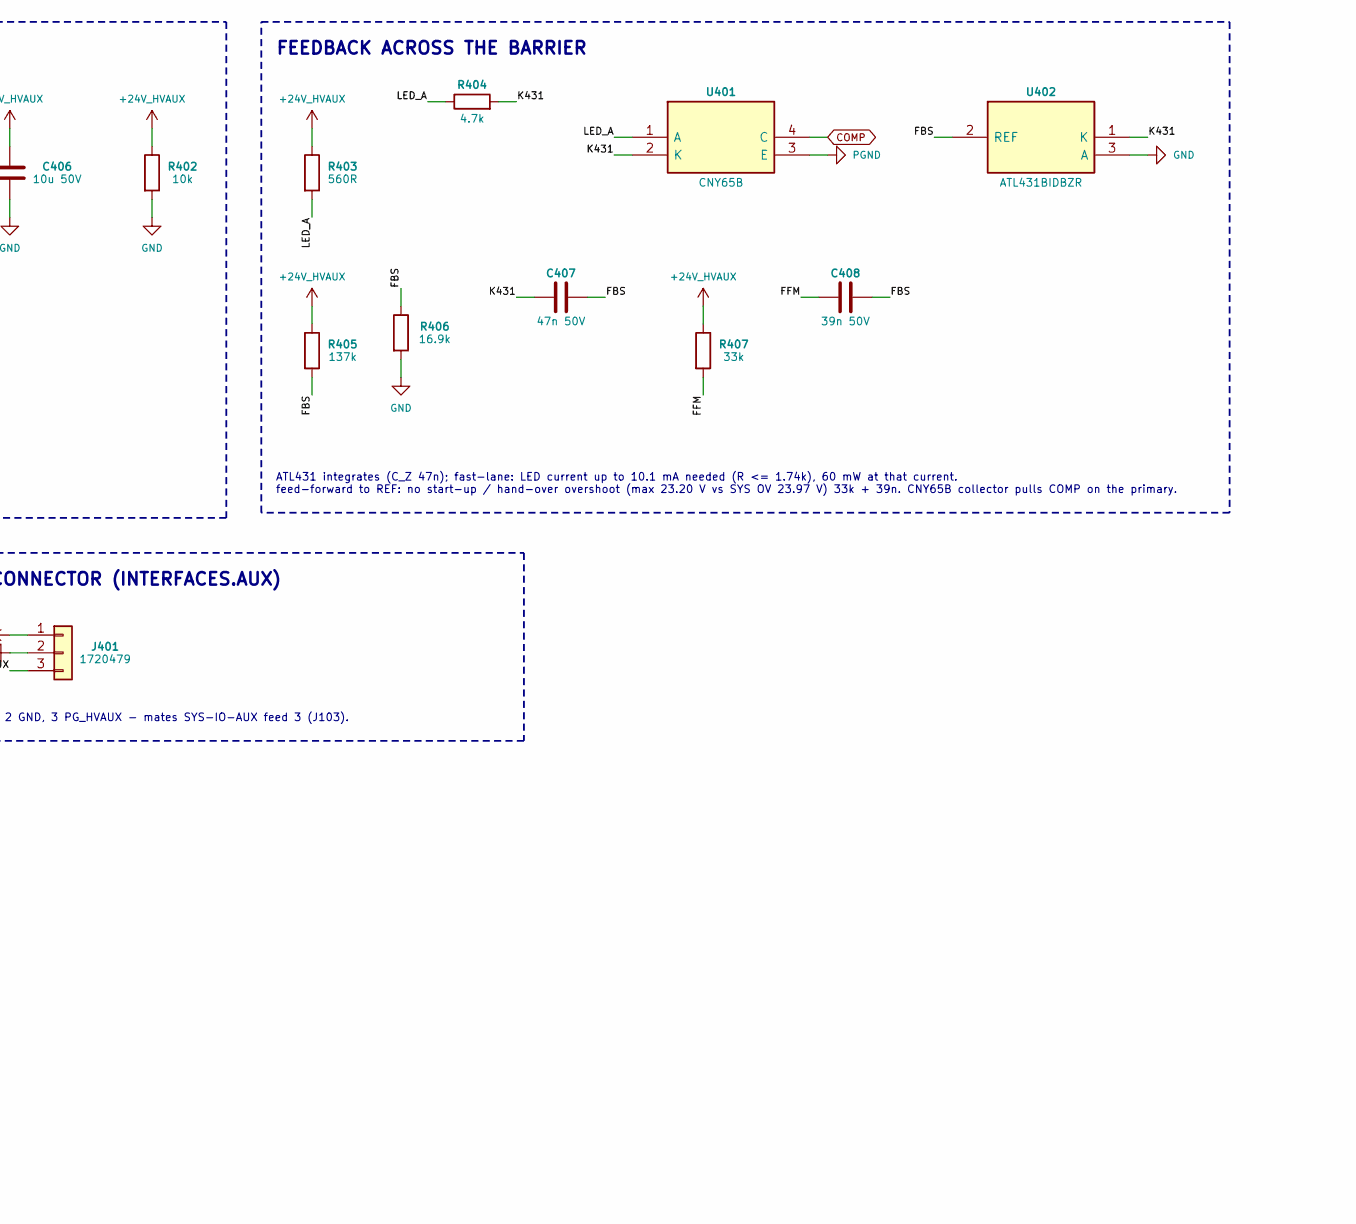
[picture p184: schematic 04_secondary.kicad_sch, part in row 1, column 2]

Parts:
C401: 68p 500V
C402, C403, C404: PCV1HVF101MB12FV-WE3; MPN PCV1HVF101MB12FV-WE3
C405, C406: 10u 50V
C407: 47n 50V
C408: 39n 50V
C409: 100n 16V
C410: 1n 50V
D401: VS-8ETU04S-M3; MPN VS-8ETU04S-M3
D402: BZX84-B3V3,215; MPN BZX84-B3V3,215
J401: 1720479; MPN 1720479
R401: 150R
R402, R408, R411, R412: 10k
R403: 560R
R404: 4.7k
R405: 137k
R406: 16.9k
R407: 33k
R409: 619k
R410: 1.82k
R413: 1k
TP401: TP
U401: CNY65B; MPN CNY65B
U402: ATL431BIDBZR; MPN ATL431BIDBZR
U403: TPS3700DDCR; MPN TPS3700DDCR
U404: SN74LVC1G17DBVR; MPN SN74LVC1G17DBVR

Connections:
+24V_HVAUX: C401.2, C402.1, C403.1, C404.1, C405.1, C406.1, D401.2 (K), J401.1, R402.1, R403.1, R405.1, R407.1, R408.1, R409.1
COMP: U401.4 (C)
FBS: C407.2, C408.2, R405.2, R406.1, U402.2 (REF)
FFM: C408.1, R407.2
GND: C402.2, C403.2, C404.2, C405.2, C406.2, C409.2, C410.2, D402.1 (A), J401.2, R402.2, R406.2, R411.2, U402.3 (A), U403.2 (GND), U404.3 (GND)
K431: C407.1, R404.2, U401.2 (K), U402.1 (K)
LED_A: R403.2, R404.1, U401.1 (A)
PG3V3: C409.1, D402.3 (K), R408.2, R412.1, U403.5 (VDD), U404.5 (VCC)
PGND: U401.3 (E)
PGO: R413.1, U404.4 (Y)
PGW: R412.2, U403.1 (OUTA), U403.6 (OUTB), U404.2 (A)
PG_HVAUX: J401.3, R413.2, TP401.1
PG_OV: R410.2, R411.1, U403.4 (INB-)
PG_UV: C410.1, R409.2, R410.1, U403.3 (INA+)
SEC_A: D401.3 (A), R401.1
SN_M: C401.1, R401.2

Notes on the sheet:
ATL431 integrates (C_Z 47n); fast-lane: LED current up to 10.1 mA needed (R <= 1.74k), 60 mW at that current. feed-forward to REF: no start-up / hand-over overshoot (max 23.20 V vs SYS OV 23.97 V) 33k + 39n. CNY65B collector pulls COMP on the primary.
1 +24V_HVAUX, 2 GND, 3 PG_HVAUX - mates SYS-IO-AUX feed 3 (J103).
FEEDBACK ACROSS THE BARRIER
RECTIFIER AND OUTPUT CAPACITORS
D2PAK tab = cathode on the quiet output node. Snubber 150R + 68p. polymer bulk: 80 mV pk-pk ripple at 600 V (calc), 0.60 A rms each. Output: Vout set point 22.770 V nominal, 22.40-23.15 V.
OUTPUT CONNECTOR (INTERFACES.AUX)
PG window: UV falling 20.61-21.39 V, OV rising 24.93-25.54 V. TPS3700 on a 3.3 V Zener rail; OUTA/OUTB low outside the window; SN74LVC1G17 (Ioff) drives the line: PG_HVAUX series resistor (high 2.51-2.77 V into the SYS 100k pull-down). Dead or unplugged -> unpowered buffer -> the SYS-IO-AUX 100k pu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
PG_HVAUX, DRIVEN ACTIVELY HIGH (INTERFACES.AUX, INT-13)
