vectivolt/PCM/hardware/BMU-GW/sheets/01_gateway.kicad_sch

## KiCad design hardware/BMU-GW/sheets/01_gateway.kicad_sch (2026-10-04)

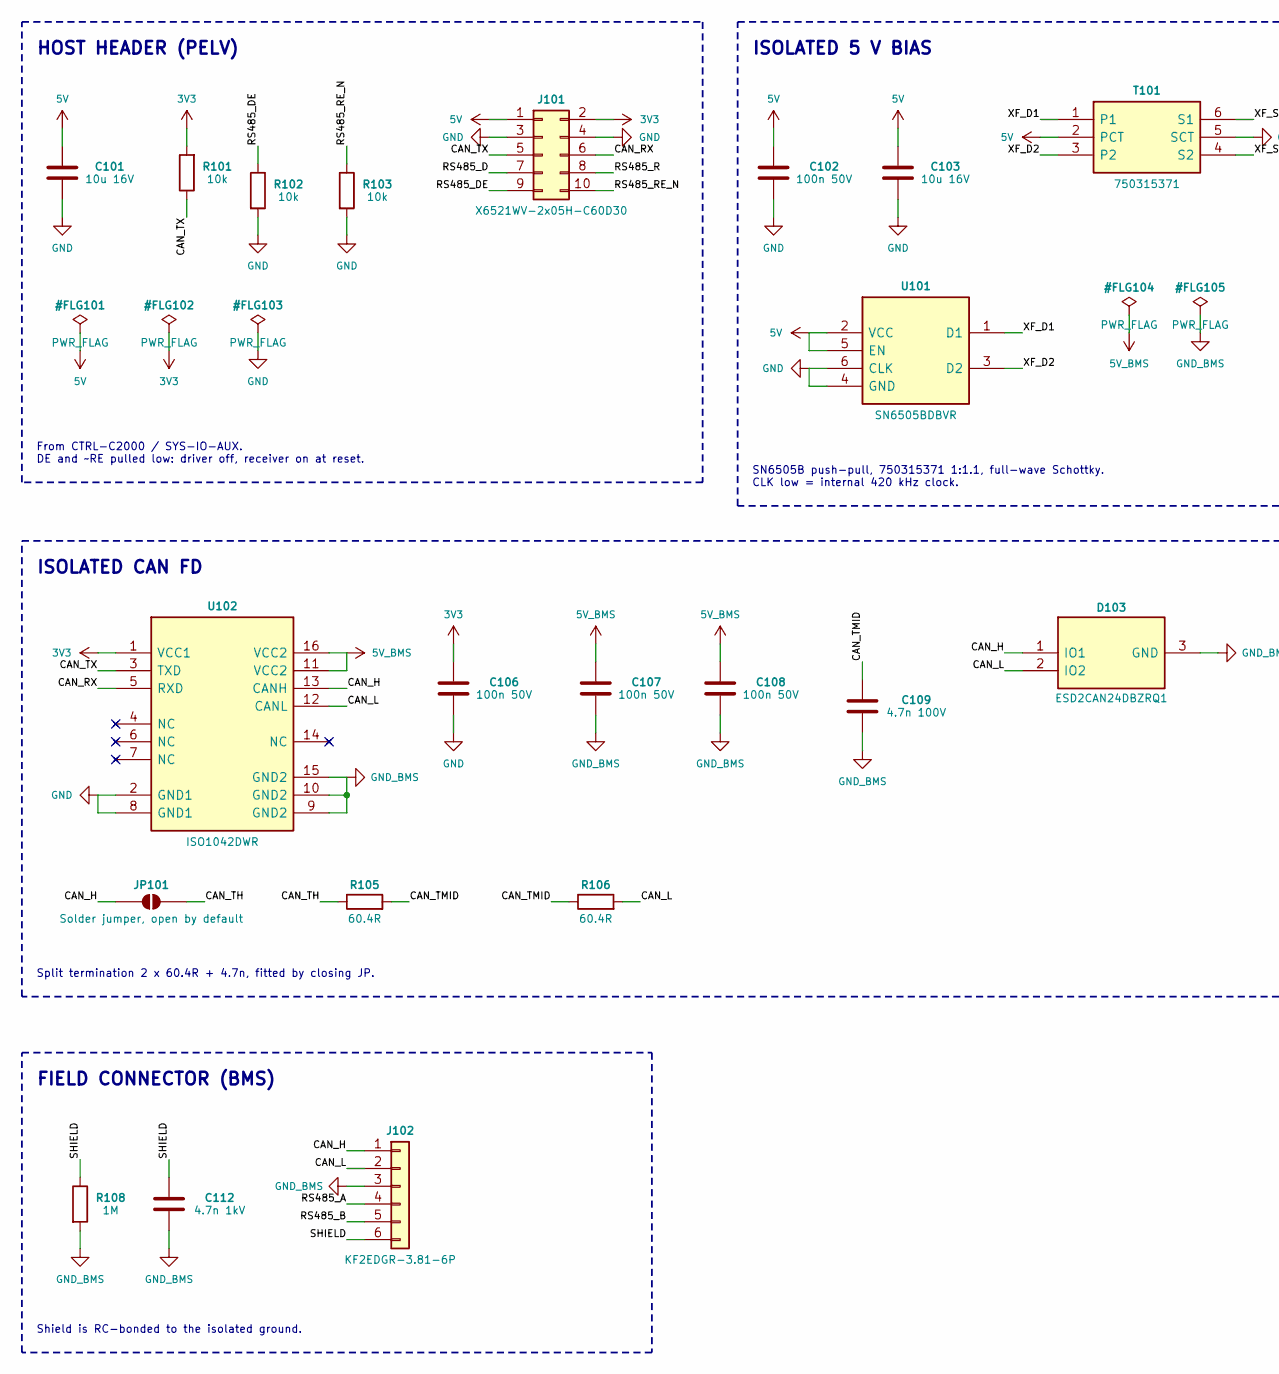
[picture p185: schematic 01_gateway.kicad_sch, part in row 1, column 1]

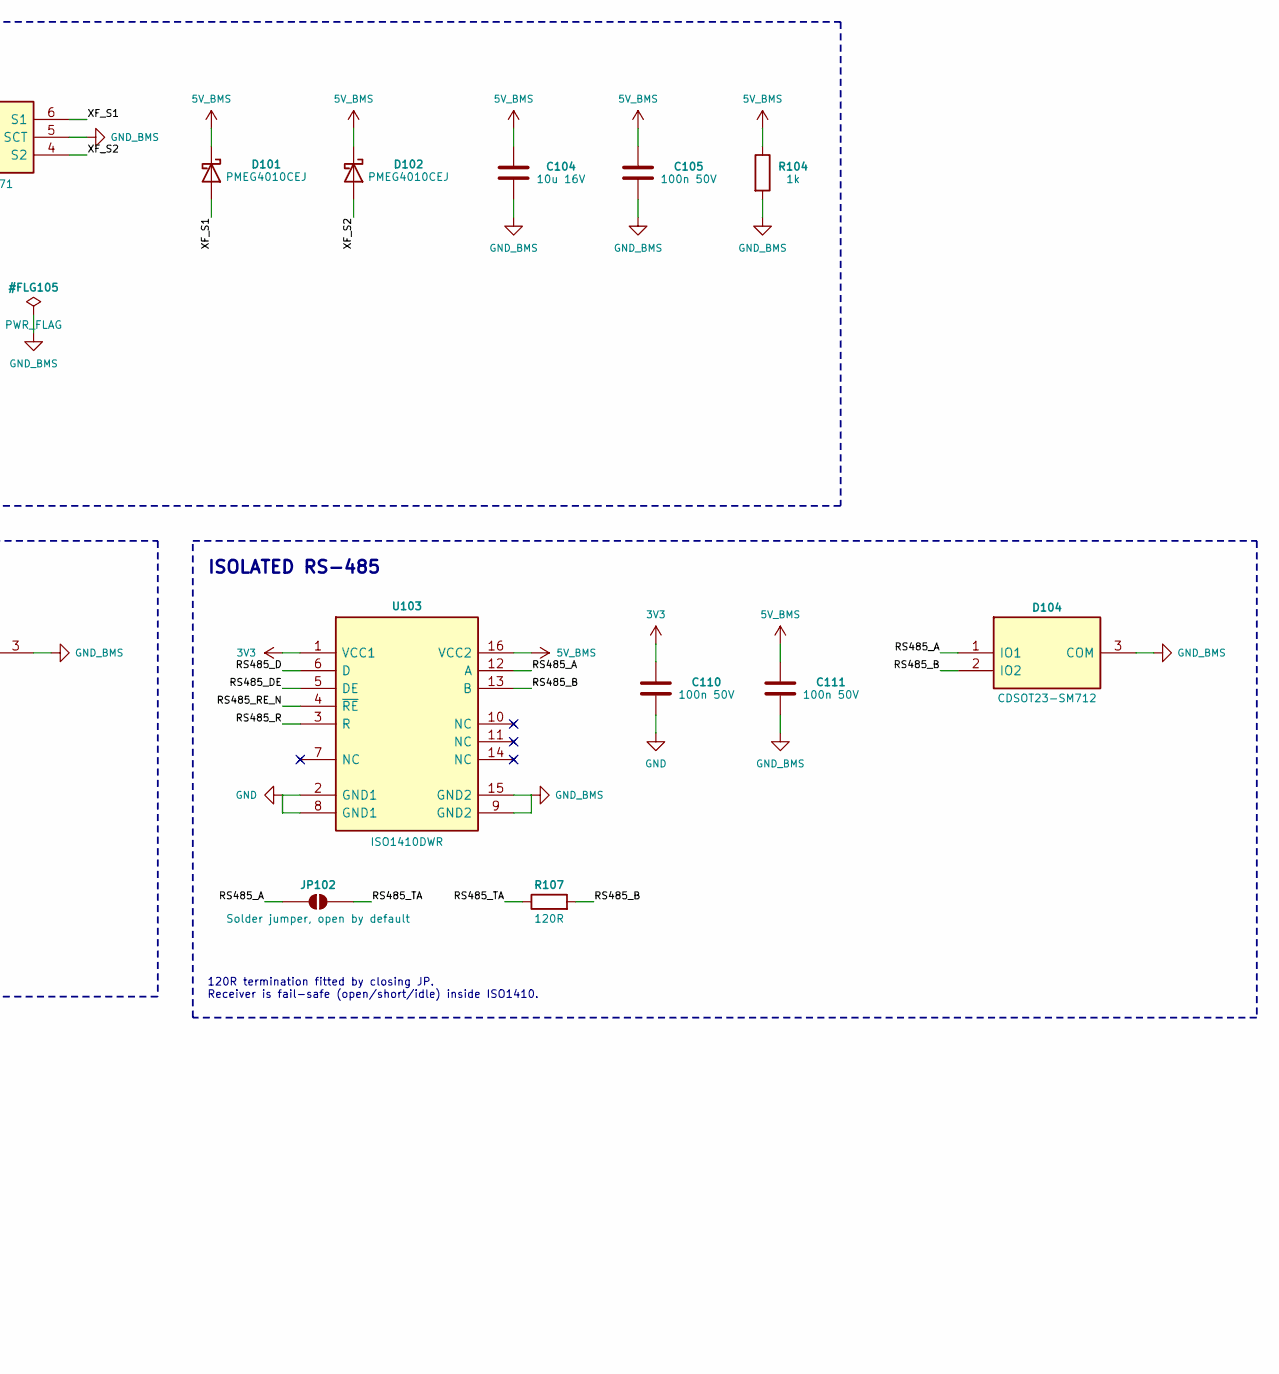
[picture p186: schematic 01_gateway.kicad_sch, part in row 1, column 2]

Parts:
C101, C103, C104: 10u 16V
C102, C105, C106, C107, C108, C110, C111: 100n 50V
C109: 4.7n 100V
C112: 4.7n 1kV
D101, D102: PMEG4010CEJ; MPN PMEG4010CEJ
D103: ESD2CAN24DBZRQ1; MPN ESD2CAN24DBZRQ1
D104: CDSOT23-SM712; MPN CDSOT23-SM712
J101: X6521WV-2x05H-C60D30; MPN X6521WV-2x05H-C60D30
J102: KF2EDGR-3.81-6P; MPN KF2EDGR-3.81-6P
JP101, JP102: Solder jumper, open by default
R101, R102, R103: 10k
R104: 1k
R105, R106: 60.4R
R107: 120R
R108: 1M
T101: 750315371; MPN 750315371
U101: SN6505BDBVR; MPN SN6505BDBVR
U102: ISO1042DWR; MPN ISO1042DWR
U103: ISO1410DWR; MPN ISO1410DWR

Connections:
3V3: C106.1, C110.1, J101.2, R101.2, U102.1 (VCC1), U103.1 (VCC1)
5V: C101.1, C102.1, C103.1, J101.1, T101.2 (PCT), U101.2 (VCC), U101.5 (EN)
5V_BMS: C104.1, C105.1, C107.1, C108.1, C111.1, D101.1 (K), D102.1 (K), R104.1, U102.11 (VCC2), U102.16 (VCC2), U103.16 (VCC2)
CAN_H: D103.1 (IO1), J102.1, JP101.1 (A), U102.13 (CANH)
CAN_L: D103.2 (IO2), J102.2, R106.2, U102.12 (CANL)
CAN_RX: J101.6, U102.5 (RXD)
CAN_TH: JP101.2 (B), R105.1
CAN_TMID: C109.1, R105.2, R106.1
CAN_TX: J101.5, R101.1, U102.3 (TXD)
GND: C101.2, C102.2, C103.2, C106.2, C110.2, J101.3, J101.4, R102.2, R103.2, U101.4 (GND), U101.6 (CLK), U102.2 (GND1), U102.8 (GND1), U103.2 (GND1), U103.8 (GND1)
GND_BMS: C104.2, C105.2, C107.2, C108.2, C109.2, C111.2, C112.2, D103.3 (GND), D104.3 (COM), J102.3, R104.2, R108.2, T101.5 (SCT), U102.9 (GND2), U102.10 (GND2), U102.15 (GND2), U103.9 (GND2), U103.15 (GND2)
RS485_A: D104.1 (IO1), J102.4, JP102.1 (A), U103.12 (A)
RS485_B: D104.2 (IO2), J102.5, R107.2, U103.13 (B)
RS485_D: J101.7, U103.6 (D)
RS485_DE: J101.9, R102.1, U103.5 (DE)
RS485_R: J101.8, U103.3 (R)
RS485_RE_N: J101.10, R103.1, U103.4 (~RE)
RS485_TA: JP102.2 (B), R107.1
SHIELD: C112.1, J102.6, R108.1
XF_D1: T101.1, U101.1 (D1)
XF_D2: T101.3 (P2), U101.3 (D2)
XF_S1: D101.2 (A), T101.6 (S1)
XF_S2: D102.2 (A), T101.4 (S2)

Notes on the sheet:
ISOLATED 5 V BIAS
SN6505B push-pull, 750315371 1:1.1, full-wave Schottky. CLK low = internal 420 kHz clock.
FIELD CONNECTOR (BMS)
From CTRL-C2000 / SYS-IO-AUX. DE and ~RE pulled low: driver off, receiver on at reset.
HOST HEADER (PELV)
Shield is RC-bonded to the isolated ground.
ISOLATED RS-485
ISOLATED CAN FD
Split termination 2 x 60.4R + 4.7n, fitted by closing JP.
120R termination fitted by closing JP. Receiver is fail-safe (open/short/idle) inside ISO1410.
