vectivolt/PCM/hardware/CTRL-C2000/sheets/01_power.kicad_sch

## KiCad design hardware/CTRL-C2000/sheets/01_power.kicad_sch (2026-10-04)

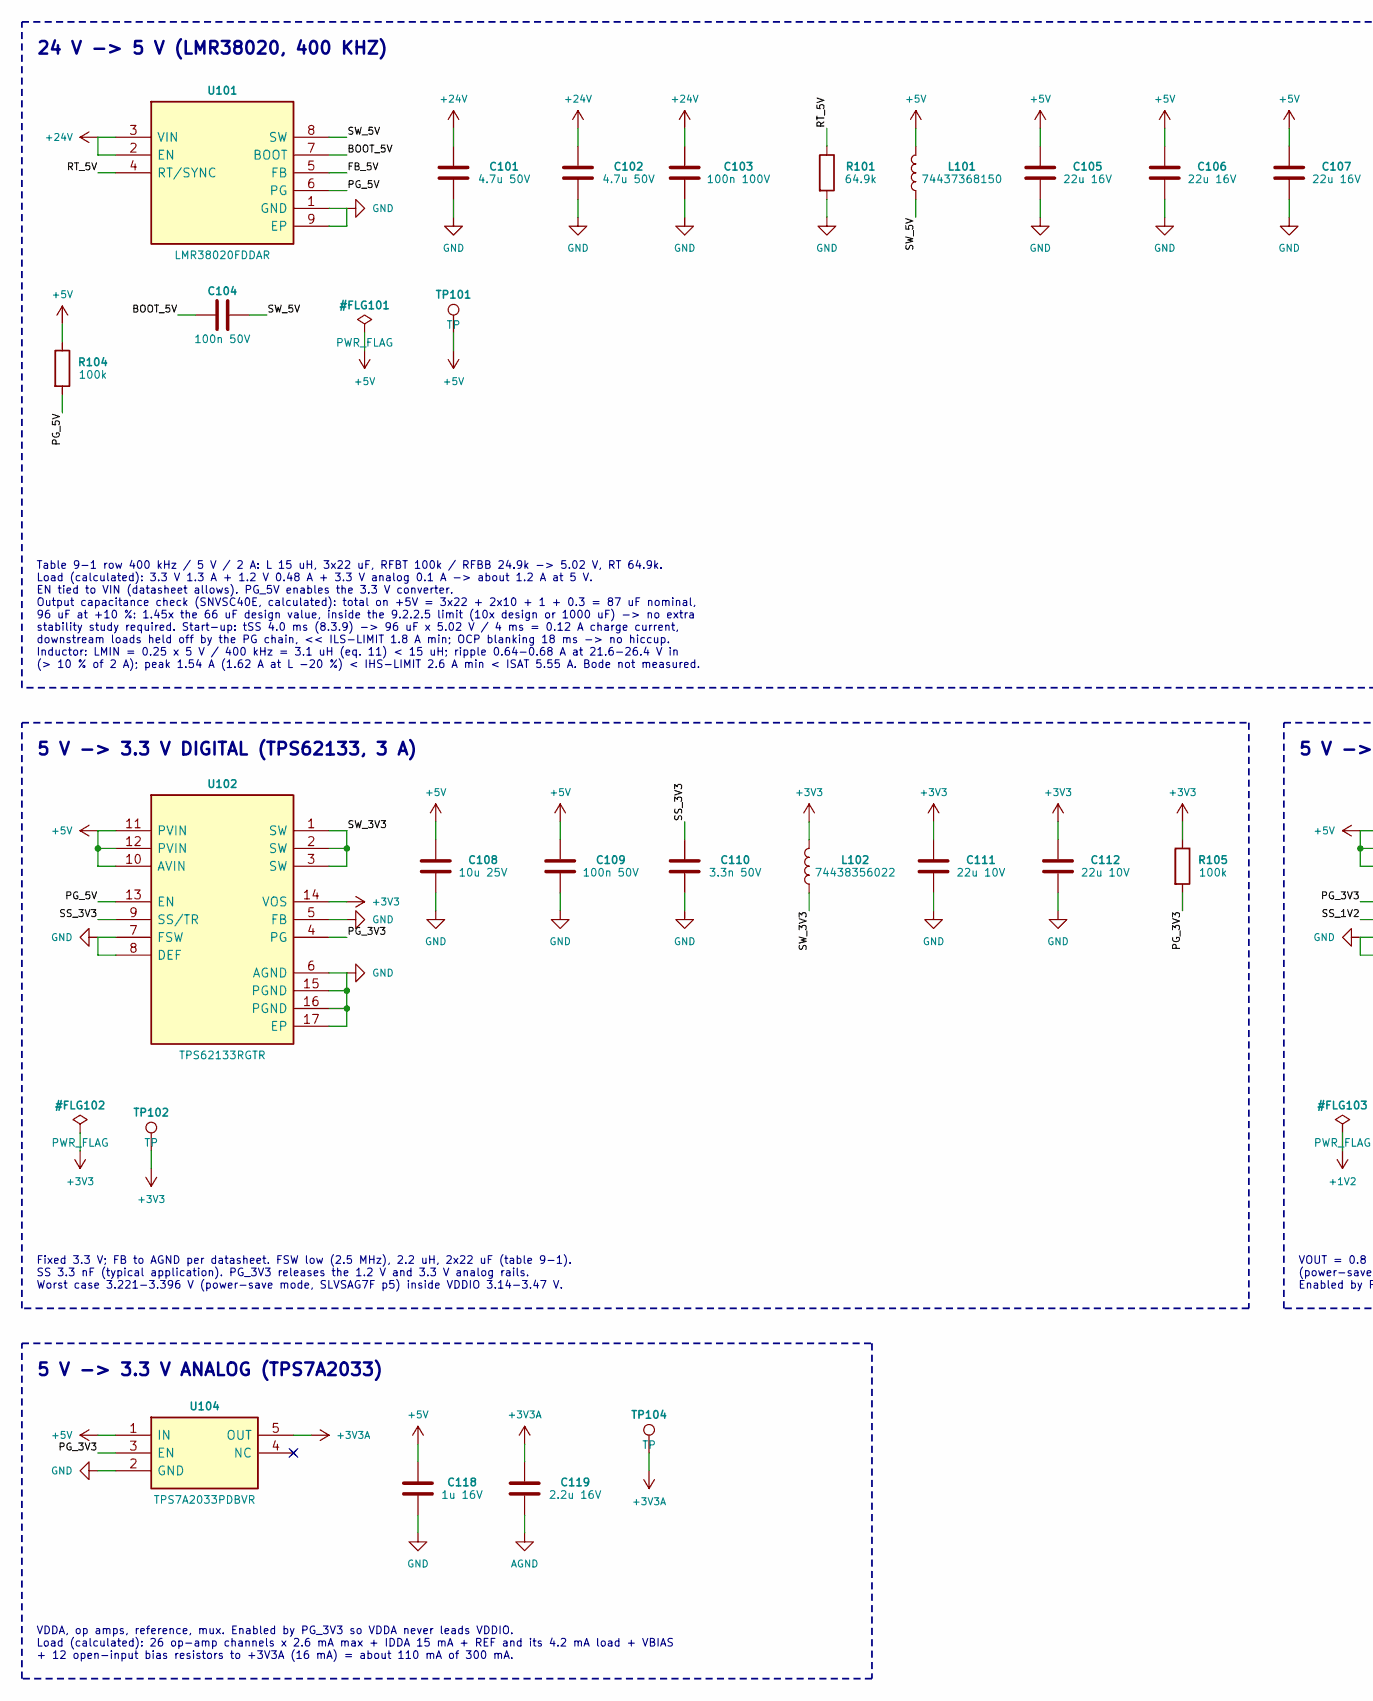
[picture p187: schematic 01_power.kicad_sch, part in row 1, column 1]

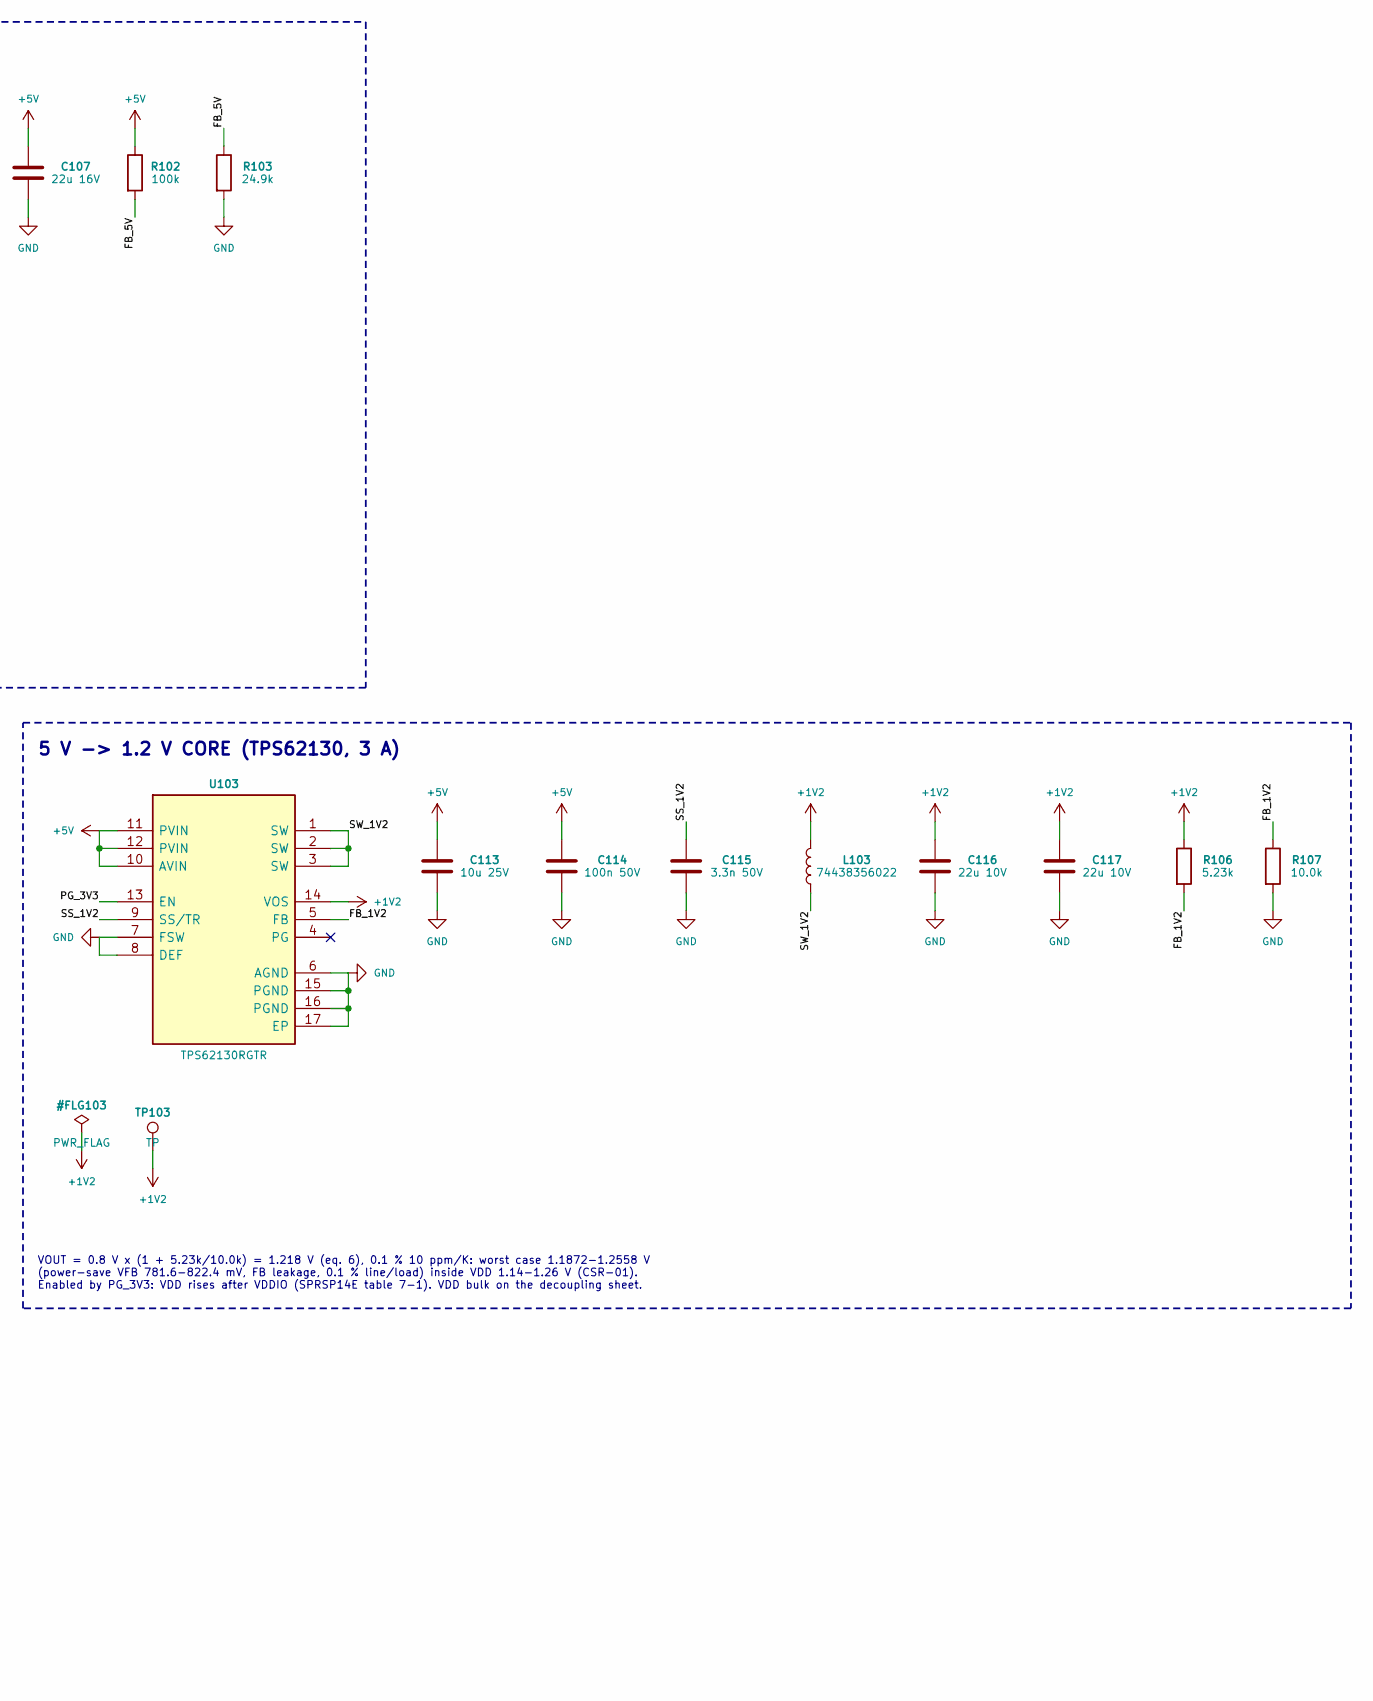
[picture p188: schematic 01_power.kicad_sch, part in row 1, column 2]

Parts:
C101, C102: 4.7u 50V
C103: 100n 100V
C104, C109, C114: 100n 50V
C105, C106, C107: 22u 16V
C108, C113: 10u 25V
C110, C115: 3.3n 50V
C111, C112, C116, C117: 22u 10V
C118: 1u 16V
C119: 2.2u 16V
L101: 74437368150; MPN 74437368150
L102, L103: 74438356022; MPN 74438356022
R101: 64.9k
R102, R104, R105: 100k
R103: 24.9k
R106: 5.23k
R107: 10.0k
TP101, TP102, TP103, TP104: TP
U101: LMR38020FDDAR; MPN LMR38020FDDAR
U102: TPS62133RGTR; MPN TPS62133RGTR
U103: TPS62130RGTR; MPN TPS62130RGTR
U104: TPS7A2033PDBVR; MPN TPS7A2033PDBVR

Connections:
+1V2: C116.1, C117.1, L103.2, R106.1, TP103.1, U103.14 (VOS)
+3V3: C111.1, C112.1, L102.2, R105.1, TP102.1, U102.14 (VOS)
+3V3A: C119.1, TP104.1, U104.5 (OUT)
+5V: C105.1, C106.1, C107.1, C108.1, C109.1, C113.1, C114.1, C118.1, L101.2, R102.1, R104.1, TP101.1, U102.10 (AVIN), U102.11 (PVIN), U102.12 (PVIN), U103.10 (AVIN), U103.11 (PVIN), U103.12 (PVIN), U104.1 (IN)
+24V: C101.1, C102.1, C103.1, U101.2 (EN), U101.3 (VIN)
AGND: C119.2
BOOT_5V: C104.1, U101.7 (BOOT)
FB_1V2: R106.2, R107.1, U103.5 (FB)
FB_5V: R102.2, R103.1, U101.5 (FB)
GND: C101.2, C102.2, C103.2, C105.2, C106.2, C107.2, C108.2, C109.2, C110.2, C111.2, C112.2, C113.2, C114.2, C115.2, C116.2, C117.2, C118.2, R101.2, R103.2, R107.2, U101.1 (GND), U101.9 (EP), U102.5 (FB), U102.6 (AGND), U102.7 (FSW), U102.8 (DEF), U102.15 (PGND), U102.16 (PGND), U102.17 (EP), U103.6 (AGND), U103.7 (FSW), U103.8 (DEF), U103.15 (PGND), U103.16 (PGND), U103.17 (EP), U104.2 (GND)
PG_3V3: R105.2, U102.4 (PG), U103.13 (EN), U104.3 (EN)
PG_5V: R104.2, U101.6 (PG), U102.13 (EN)
RT_5V: R101.1, U101.4 (RT/SYNC)
SS_1V2: C115.1, U103.9 (SS/TR)
SS_3V3: C110.1, U102.9 (SS/TR)
SW_1V2: L103.1, U103.1 (SW), U103.2 (SW), U103.3 (SW)
SW_3V3: L102.1, U102.1 (SW), U102.2 (SW), U102.3 (SW)
SW_5V: C104.2, L101.1, U101.8 (SW)

Notes on the sheet:
Fixed 3.3 V; FB to AGND per datasheet. FSW low (2.5 MHz), 2.2 uH, 2x22 uF (table 9-1). SS 3.3 nF (typical application). PG_3V3 releases the 1.2 V and 3.3 V analog rails. Worst case 3.221-3.396 V (power-save mode, SLVSAG7F p5) inside VDDIO 3.14-3.47 V.
5 V -> 3.3 V DIGITAL (TPS62133, 3 A)
5 V -> 3.3 V ANALOG (TPS7A2033)
VOUT = 0.8 V x (1 + 5.23k/10.0k) = 1.218 V (eq. 6), 0.1 % 10 ppm/K: worst case 1.1872-1.2558 V (power-save VFB 781.6-822.4 mV, FB leakage, 0.1 % line/load) inside VDD 1.14-1.26 V (CSR-01). Enabled by PG_3V3: VDD rises after VDDIO (SPRSP14E table 7-1). VDD bulk on the decoupling sheet.
5 V -> 1.2 V CORE (TPS62130, 3 A)
Table 9-1 row 400 kHz / 5 V / 2 A: L 15 uH, 3x22 uF, RFBT 100k / RFBB 24.9k -> 5.02 V, RT 64.9k. Load (calculated): 3.3 V 1.3 A + 1.2 V 0.48 A + 3.3 V analog 0.1 A -> about 1.2 A at 5 V. EN tied to VIN (datasheet allows). PG_5V enables the 3.3 V converter. Output capacitance check (SNVSC40E, calcul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
24 V -> 5 V (LMR38020, 400 KHZ)
VDDA, op amps, reference, mux. Enabled by PG_3V3 so VDDA never leads VDDIO. Load (calculated): 26 op-amp channels x 2.6 mA max + IDDA 15 mA + REF and its 4.2 mA load + VBIAS + 12 open-input bias resistors to +3V3A (16 mA) = about 110 mA of 300 mA.
