vectivolt/PCM/hardware/CTRL-C2000/sheets/02_reset.kicad_sch

## KiCad design hardware/CTRL-C2000/sheets/02_reset.kicad_sch (2026-10-04)

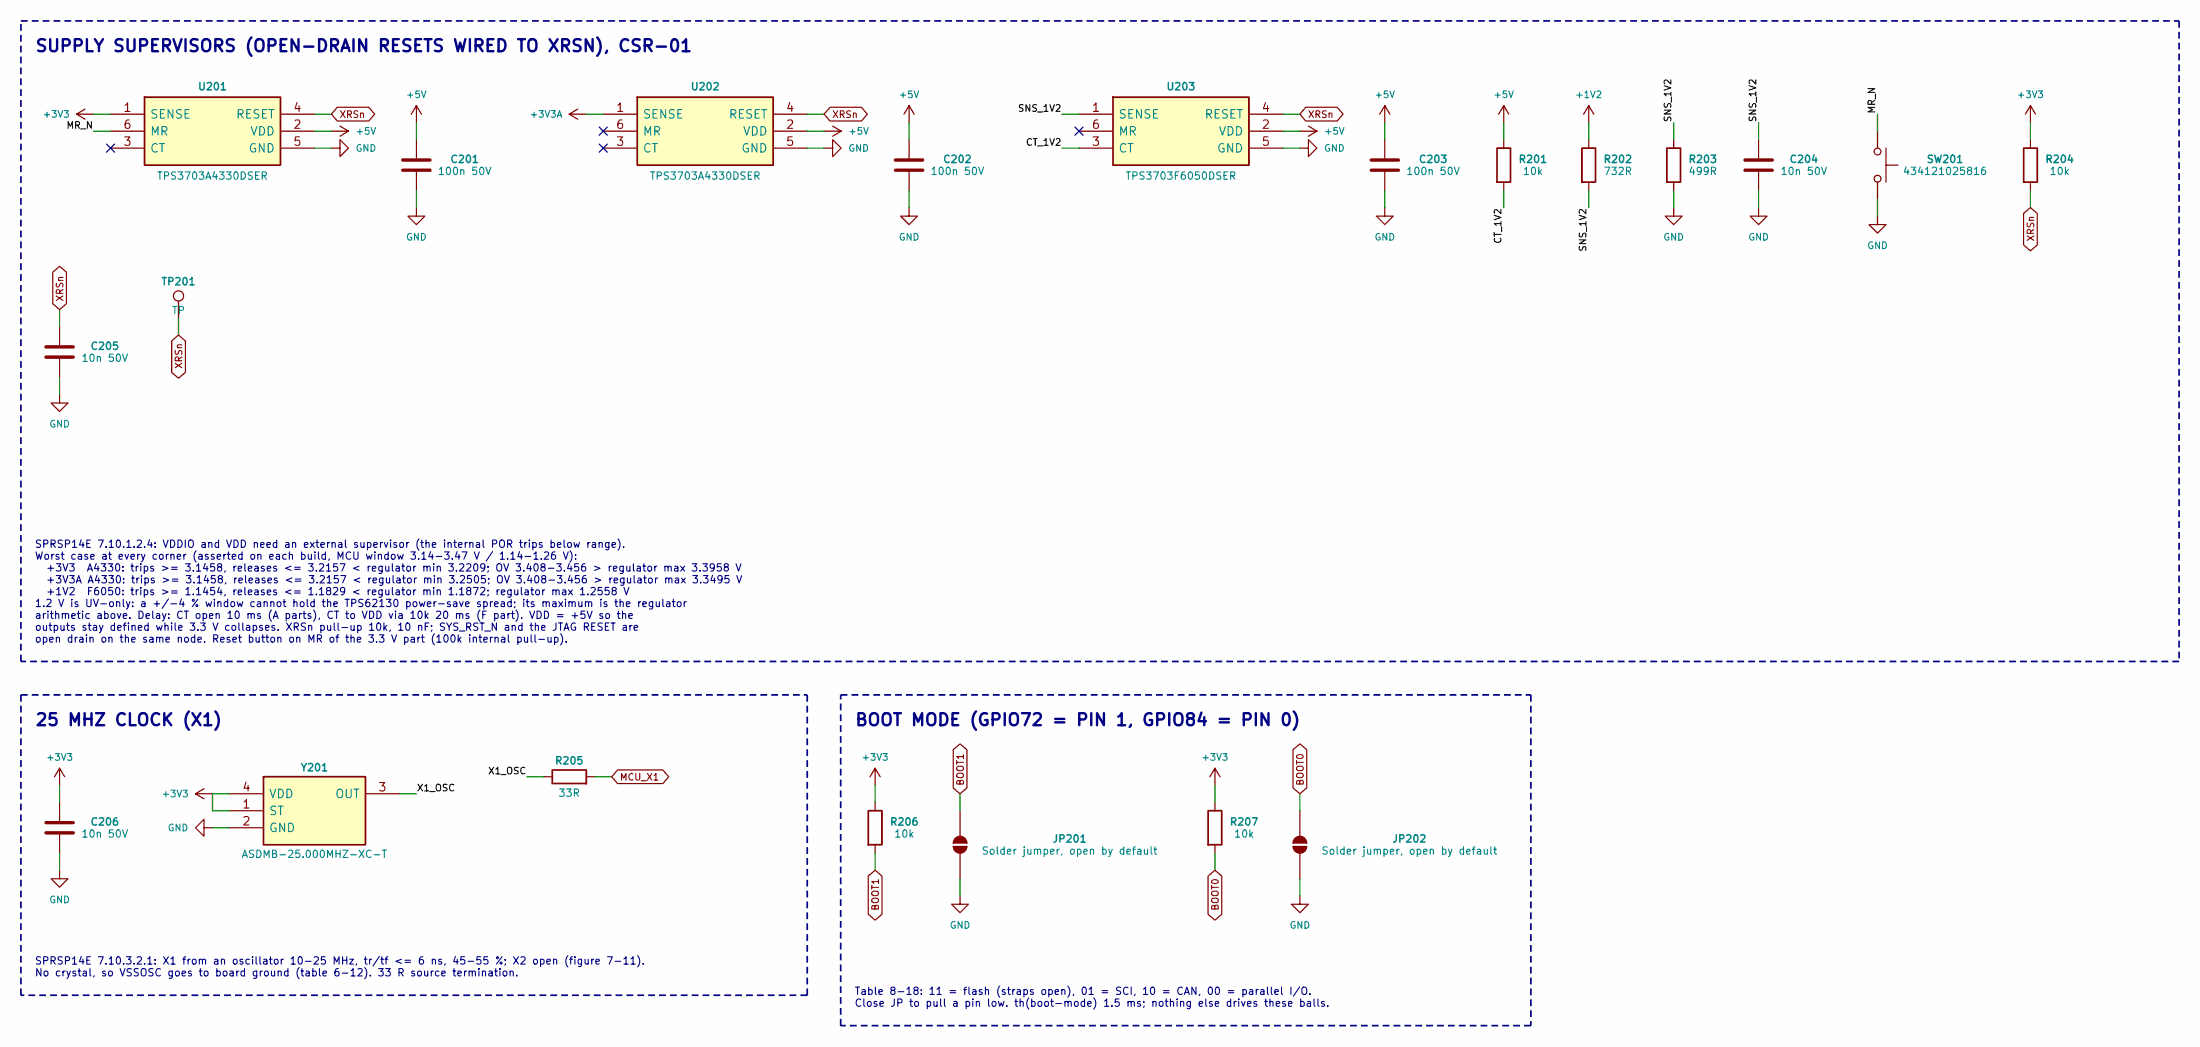
[picture p189: schematic 02_reset.kicad_sch]

Parts:
C201, C202, C203: 100n 50V
C204, C205, C206: 10n 50V
JP201, JP202: Solder jumper, open by default
R201, R204, R206, R207: 10k
R202: 732R
R203: 499R
R205: 33R
SW201: 434121025816; MPN 434121025816
TP201: TP
U201, U202: TPS3703A4330DSER; MPN TPS3703A4330DSER
U203: TPS3703F6050DSER; MPN TPS3703F6050DSER
Y201: ASDMB-25.000MHZ-XC-T; MPN ASDMB-25.000MHZ-XC-T

Connections:
+1V2: R202.1
+3V3: C206.1, R204.1, R206.1, R207.1, U201.1 (SENSE), Y201.1 (ST), Y201.4 (VDD)
+3V3A: U202.1 (SENSE)
+5V: C201.1, C202.1, C203.1, R201.1, U201.2 (VDD), U202.2 (VDD), U203.2 (VDD)
BOOT0: JP202.1 (A), R207.2
BOOT1: JP201.1 (A), R206.2
CT_1V2: R201.2, U203.3 (CT)
GND: C201.2, C202.2, C203.2, C204.2, C205.2, C206.2, JP201.2 (B), JP202.2 (B), R203.2, SW201.2, U201.5 (GND), U202.5 (GND), U203.5 (GND), Y201.2 (GND)
MCU_X1: R205.2
MR_N: SW201.1, U201.6 (MR)
SNS_1V2: C204.1, R202.2, R203.1, U203.1 (SENSE)
X1_OSC: R205.1, Y201.3 (OUT)
XRSn: C205.1, R204.2, TP201.1, U201.4 (RESET), U202.4 (RESET), U203.4 (RESET)

Notes on the sheet:
SPRSP14E 7.10.1.2.4: VDDIO and VDD need an external supervisor (the internal POR trips below range). Worst case at every corner (asserted on each build, MCU window 3.14-3.47 V / 1.14-1.26 V): +3V3 A4330: trips >= 3.1458, releases <= 3.2157 < regulator min 3.2209; OV 3.408-3.456 > regulator max 3.39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
BOOT MODE (GPIO72 = PIN 1, GPIO84 = PIN 0)
SPRSP14E 7.10.3.2.1: X1 from an oscillator 10-25 MHz, tr/tf <= 6 ns, 45-55 %; X2 open (figure 7-11). No crystal, so VSSOSC goes to board ground (table 6-12). 33 R source termination.
Table 8-18: 11 = flash (straps open), 01 = SCI, 10 = CAN, 00 = parallel I/O. Close JP to pull a pin low. th(boot-mode) 1.5 ms; nothing else drives these balls.
SUPPLY SUPERVISORS (OPEN-DRAIN RESETS WIRED TO XRSN), CSR-01
25 MHZ CLOCK (X1)
