vectivolt/PCM/hardware/CTRL-C2000/sheets/04_decoupling.kicad_sch

## KiCad design hardware/CTRL-C2000/sheets/04_decoupling.kicad_sch (2026-10-04)

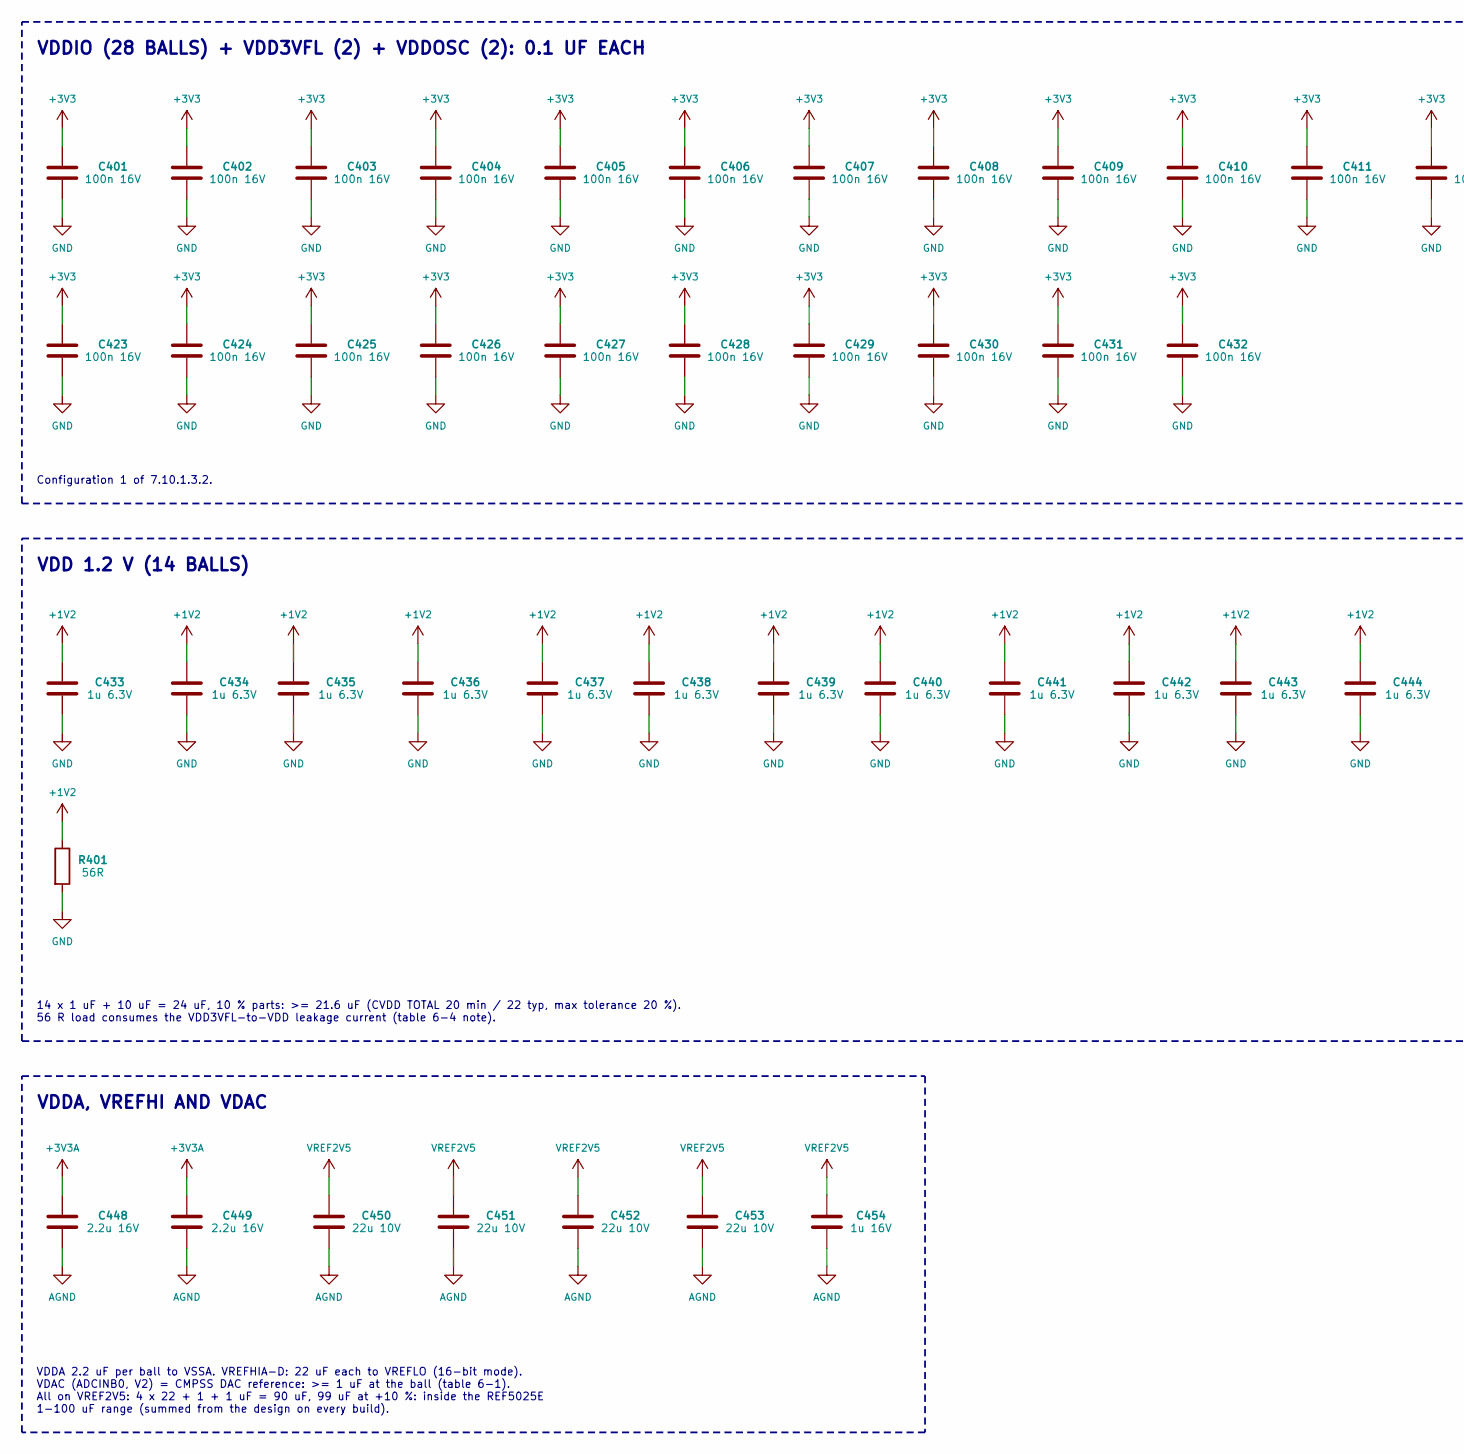
[picture p190: schematic 04_decoupling.kicad_sch, part in row 1, column 1]

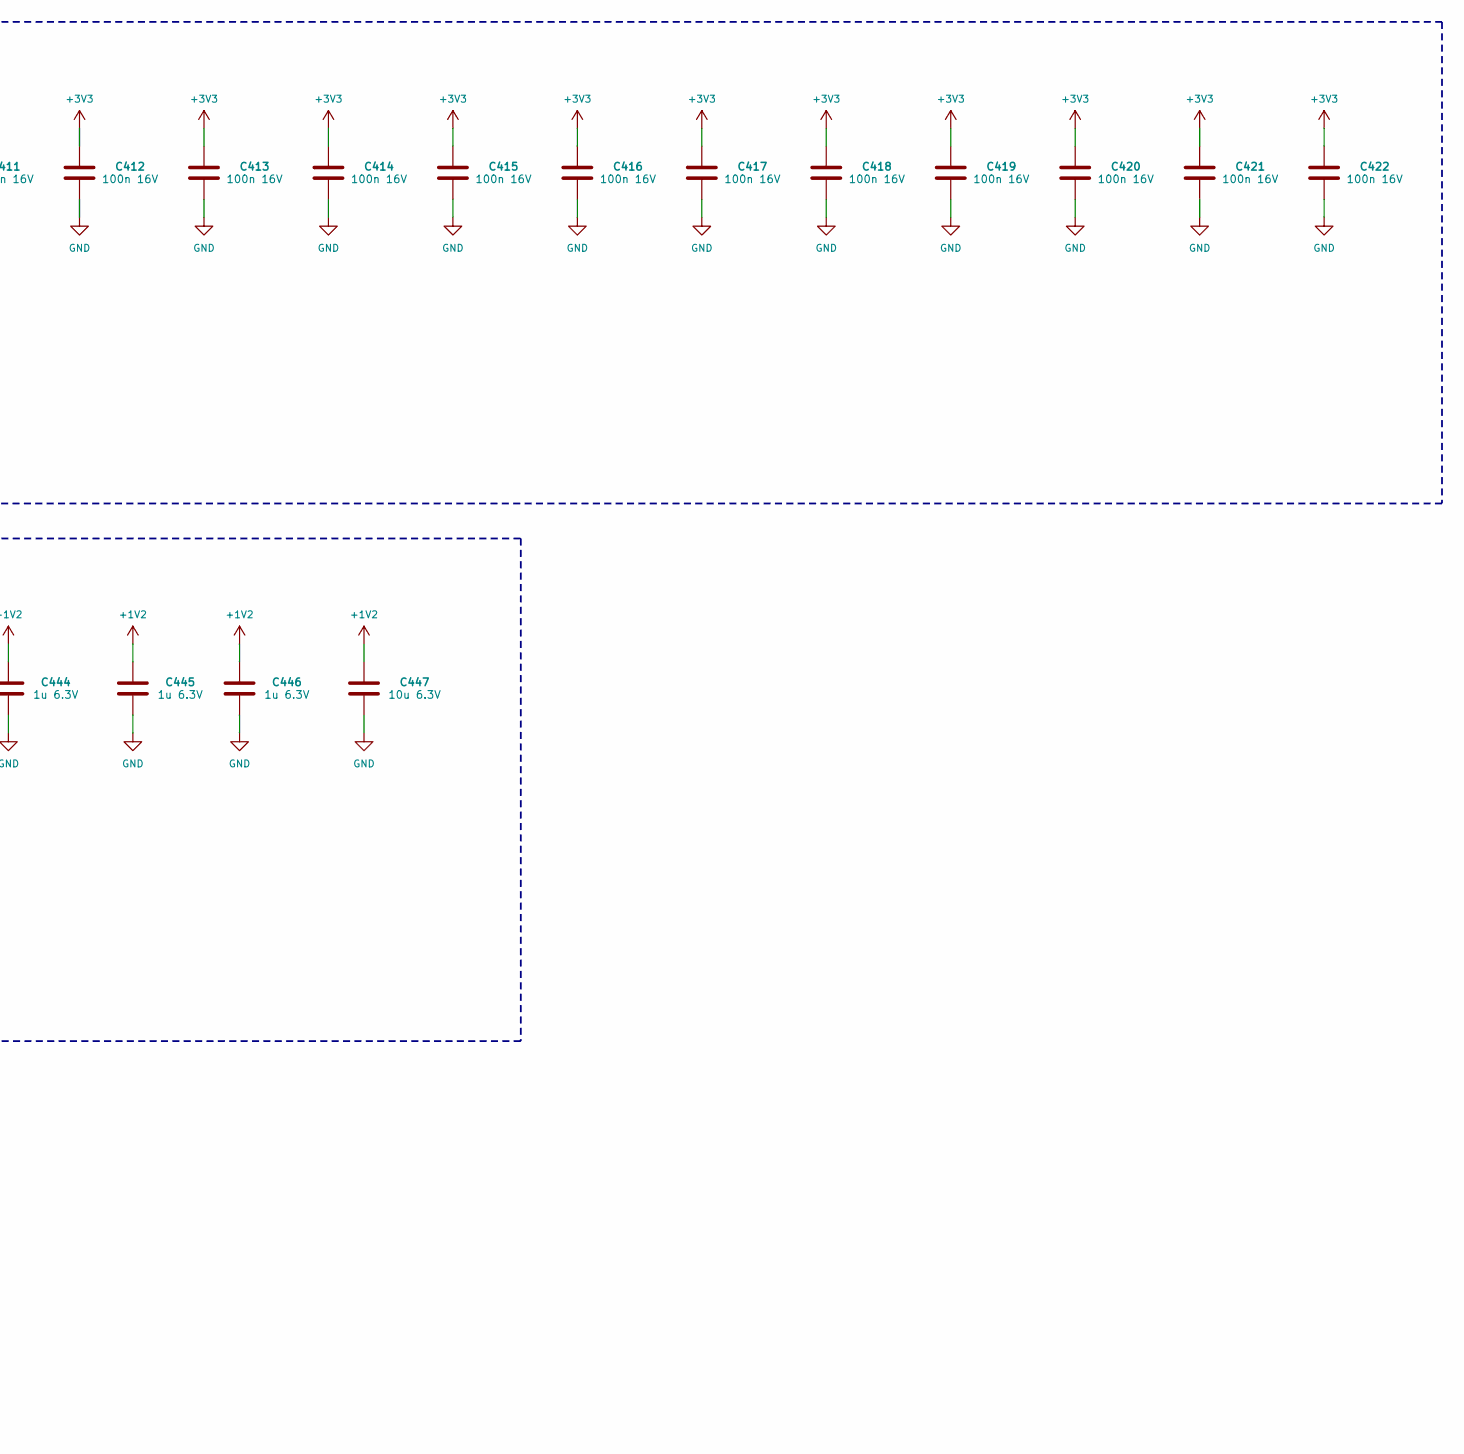
[picture p191: schematic 04_decoupling.kicad_sch, part in row 1, column 2]

Parts:
C401, C402, C403, C404, C405, C406, C407, C408, C409, C410, C411, C412, C413, C414, C415, C416, C417, C418, C419, C420, C421, C422, C423, C424, C425, C426, C427, C428, C429, C430, C431, C432: 100n 16V
C433, C434, C435, C436, C437, C438, C439, C440, C441, C442, C443, C444, C445, C446: 1u 6.3V
C447: 10u 6.3V
C448, C449: 2.2u 16V
C450, C451, C452, C453: 22u 10V
C454: 1u 16V
R401: 56R

Connections:
+1V2: C433.1, C434.1, C435.1, C436.1, C437.1, C438.1, C439.1, C440.1, C441.1, C442.1, C443.1, C444.1, C445.1, C446.1, C447.1, R401.1
+3V3: C401.1, C402.1, C403.1, C404.1, C405.1, C406.1, C407.1, C408.1, C409.1, C410.1, C411.1, C412.1, C413.1, C414.1, C415.1, C416.1, C417.1, C418.1, C419.1, C420.1, C421.1, C422.1, C423.1, C424.1, C425.1, C426.1, C427.1, C428.1, C429.1, C430.1, C431.1, C432.1
+3V3A: C448.1, C449.1
AGND: C448.2, C449.2, C450.2, C451.2, C452.2, C453.2, C454.2
GND: C401.2, C402.2, C403.2, C404.2, C405.2, C406.2, C407.2, C408.2, C409.2, C410.2, C411.2, C412.2, C413.2, C414.2, C415.2, C416.2, C417.2, C418.2, C419.2, C420.2, C421.2, C422.2, C423.2, C424.2, C425.2, C426.2, C427.2, C428.2, C429.2, C430.2, C431.2, C432.2, C433.2, C434.2, C435.2, C436.2, C437.2, C438.2, C439.2, C440.2, C441.2, C442.2, C443.2, C444.2, C445.2, C446.2, C447.2, R401.2
VREF2V5: C450.1, C451.1, C452.1, C453.1, C454.1

Notes on the sheet:
14 x 1 uF + 10 uF = 24 uF, 10 % parts: >= 21.6 uF (CVDD TOTAL 20 min / 22 typ, max tolerance 20 %). 56 R load consumes the VDD3VFL-to-VDD leakage current (table 6-4 note).
VDD 1.2 V (14 BALLS)
Configuration 1 of 7.10.1.3.2.
VDDIO (28 BALLS) + VDD3VFL (2) + VDDOSC (2): 0.1 UF EACH
VDDA 2.2 uF per ball to VSSA. VREFHIA-D: 22 uF each to VREFLO (16-bit mode). VDAC (ADCINB0, V2) = CMPSS DAC reference: >= 1 uF at the ball (table 6-1). All on VREF2V5: 4 x 22 + 1 + 1 uF = 90 uF, 99 uF at +10 %: inside the REF5025E 1-100 uF range (summed from the design on every build).
VDDA, VREFHI AND VDAC
