vectivolt/PCM/hardware/CTRL-C2000/sheets/05_adcref.kicad_sch

## KiCad design hardware/CTRL-C2000/sheets/05_adcref.kicad_sch (2026-10-04)

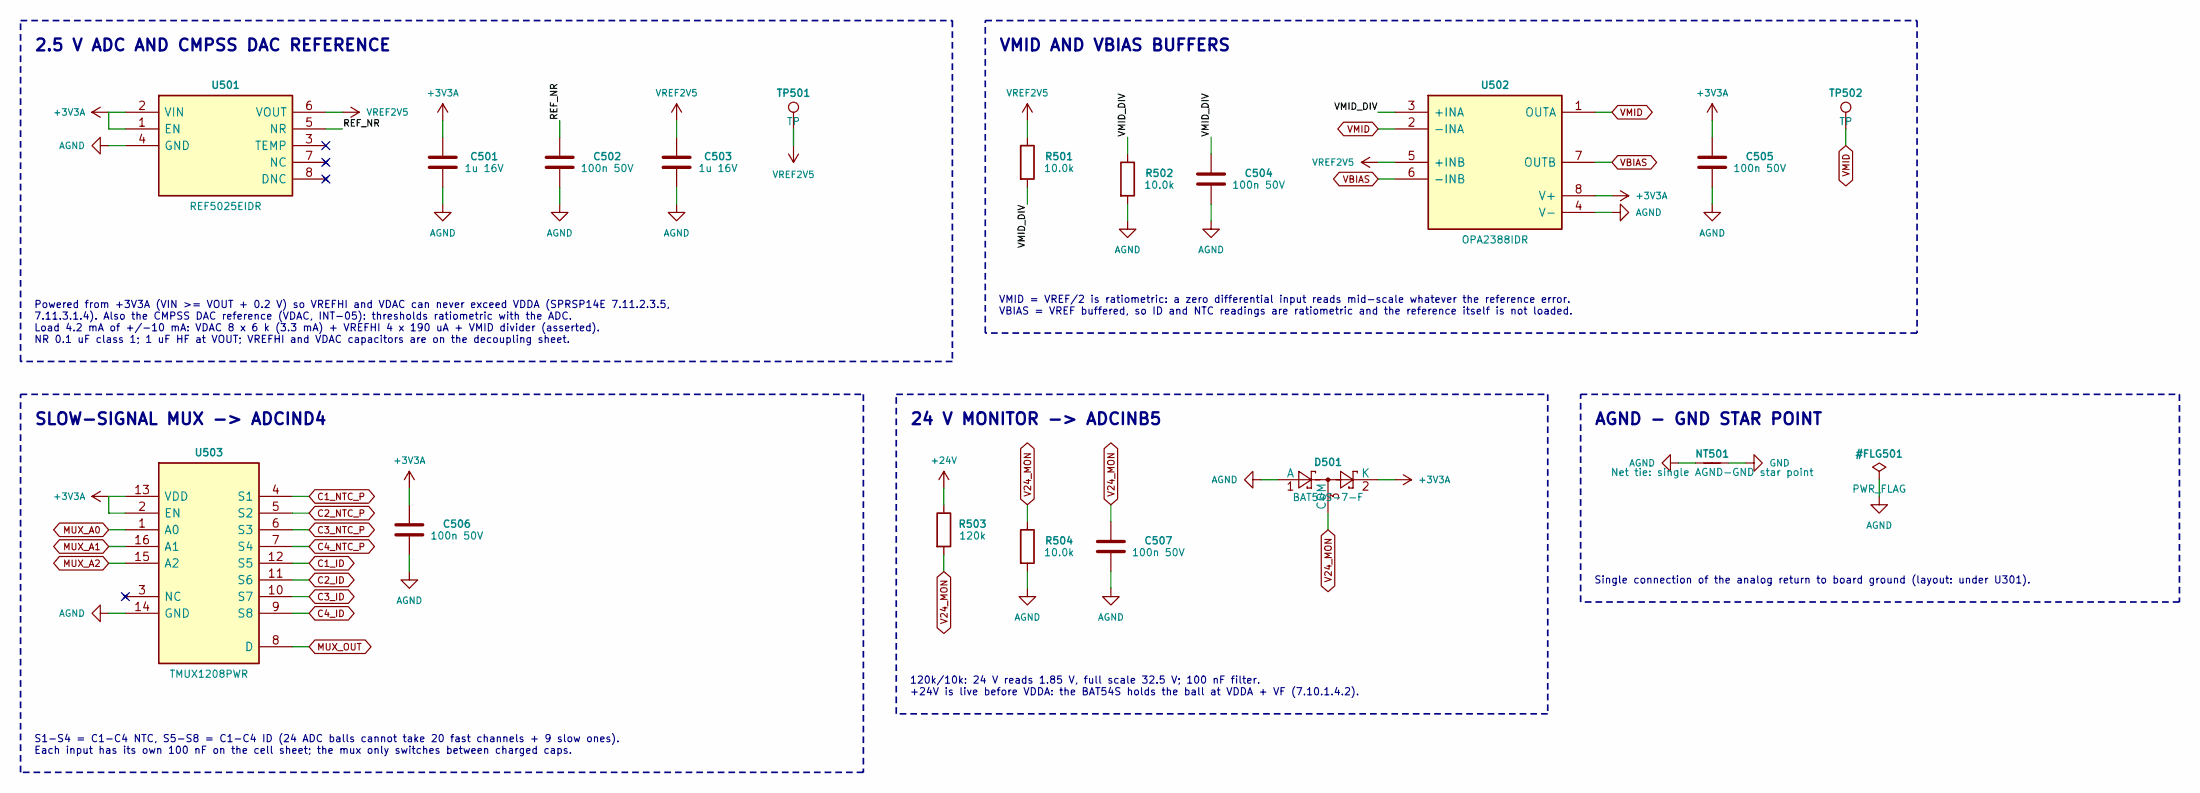
[picture p192: schematic 05_adcref.kicad_sch]

Parts:
C501, C503: 1u 16V
C502, C504, C505, C506, C507: 100n 50V
D501: BAT54S-7-F; MPN BAT54S-7-F
NT501: Net tie: single AGND-GND star point
R501, R502, R504: 10.0k
R503: 120k
TP501, TP502: TP
U501: REF5025EIDR; MPN REF5025EIDR
U502: OPA2388IDR; MPN OPA2388IDR
U503: TMUX1208PWR; MPN TMUX1208PWR

Connections:
+3V3A: C501.1, C505.1, C506.1, D501.2 (K), U501.1 (EN), U501.2 (VIN), U502.8 (V+), U503.2 (EN), U503.13 (VDD)
+24V: R503.1
AGND: C501.2, C502.2, C503.2, C504.2, C505.2, C506.2, C507.2, D501.1 (A), NT501.1, R502.2, R504.2, U501.4 (GND), U502.4 (V-), U503.14 (GND)
C1_ID: U503.12 (S5)
C1_NTC_P: U503.4 (S1)
C2_ID: U503.11 (S6)
C2_NTC_P: U503.5 (S2)
C3_ID: U503.10 (S7)
C3_NTC_P: U503.6 (S3)
C4_ID: U503.9 (S8)
C4_NTC_P: U503.7 (S4)
GND: NT501.2
MUX_A0: U503.1 (A0)
MUX_A1: U503.16 (A1)
MUX_A2: U503.15 (A2)
MUX_OUT: U503.8 (D)
REF_NR: C502.1, U501.5 (NR)
V24_MON: C507.1, D501.3 (COM), R503.2, R504.1
VBIAS: U502.6 (-INB), U502.7 (OUTB)
VMID: TP502.1, U502.1 (OUTA), U502.2 (-INA)
VMID_DIV: C504.1, R501.2, R502.1, U502.3 (+INA)
VREF2V5: C503.1, R501.1, TP501.1, U501.6 (VOUT), U502.5 (+INB)

Notes on the sheet:
SLOW-SIGNAL MUX -> ADCIND4
120k/10k: 24 V reads 1.85 V, full scale 32.5 V; 100 nF filter. +24V is live before VDDA: the BAT54S holds the ball at VDDA + VF (7.10.1.4.2).
AGND - GND STAR POINT
Single connection of the analog return to board ground (layout: under U301).
VMID AND VBIAS BUFFERS
VMID = VREF/2 is ratiometric: a zero differential input reads mid-scale whatever the reference error. VBIAS = VREF buffered, so ID and NTC readings are ratiometric and the reference itself is not loaded.
S1-S4 = C1-C4 NTC, S5-S8 = C1-C4 ID (24 ADC balls cannot take 20 fast channels + 9 slow ones). Each input has its own 100 nF on the cell sheet; the mux only switches between charged caps.
Powered from +3V3A (VIN >= VOUT + 0.2 V) so VREFHI and VDAC can never exceed VDDA (SPRSP14E 7.11.2.3.5, 7.11.3.1.4). Also the CMPSS DAC reference (VDAC, INT-05): thresholds ratiometric with the ADC. Load 4.2 mA of +/-10 mA: VDAC 8 x 6 k (3.3 mA) + VREFHI 4 x 190 uA + VMID divider (asserted). NR 0.1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
24 V MONITOR -> ADCINB5
2.5 V ADC AND CMPSS DAC REFERENCE
