vectivolt/PCM/hardware/CTRL-C2000/sheets/06_trip.kicad_sch

## KiCad design hardware/CTRL-C2000/sheets/06_trip.kicad_sch (2026-10-04)

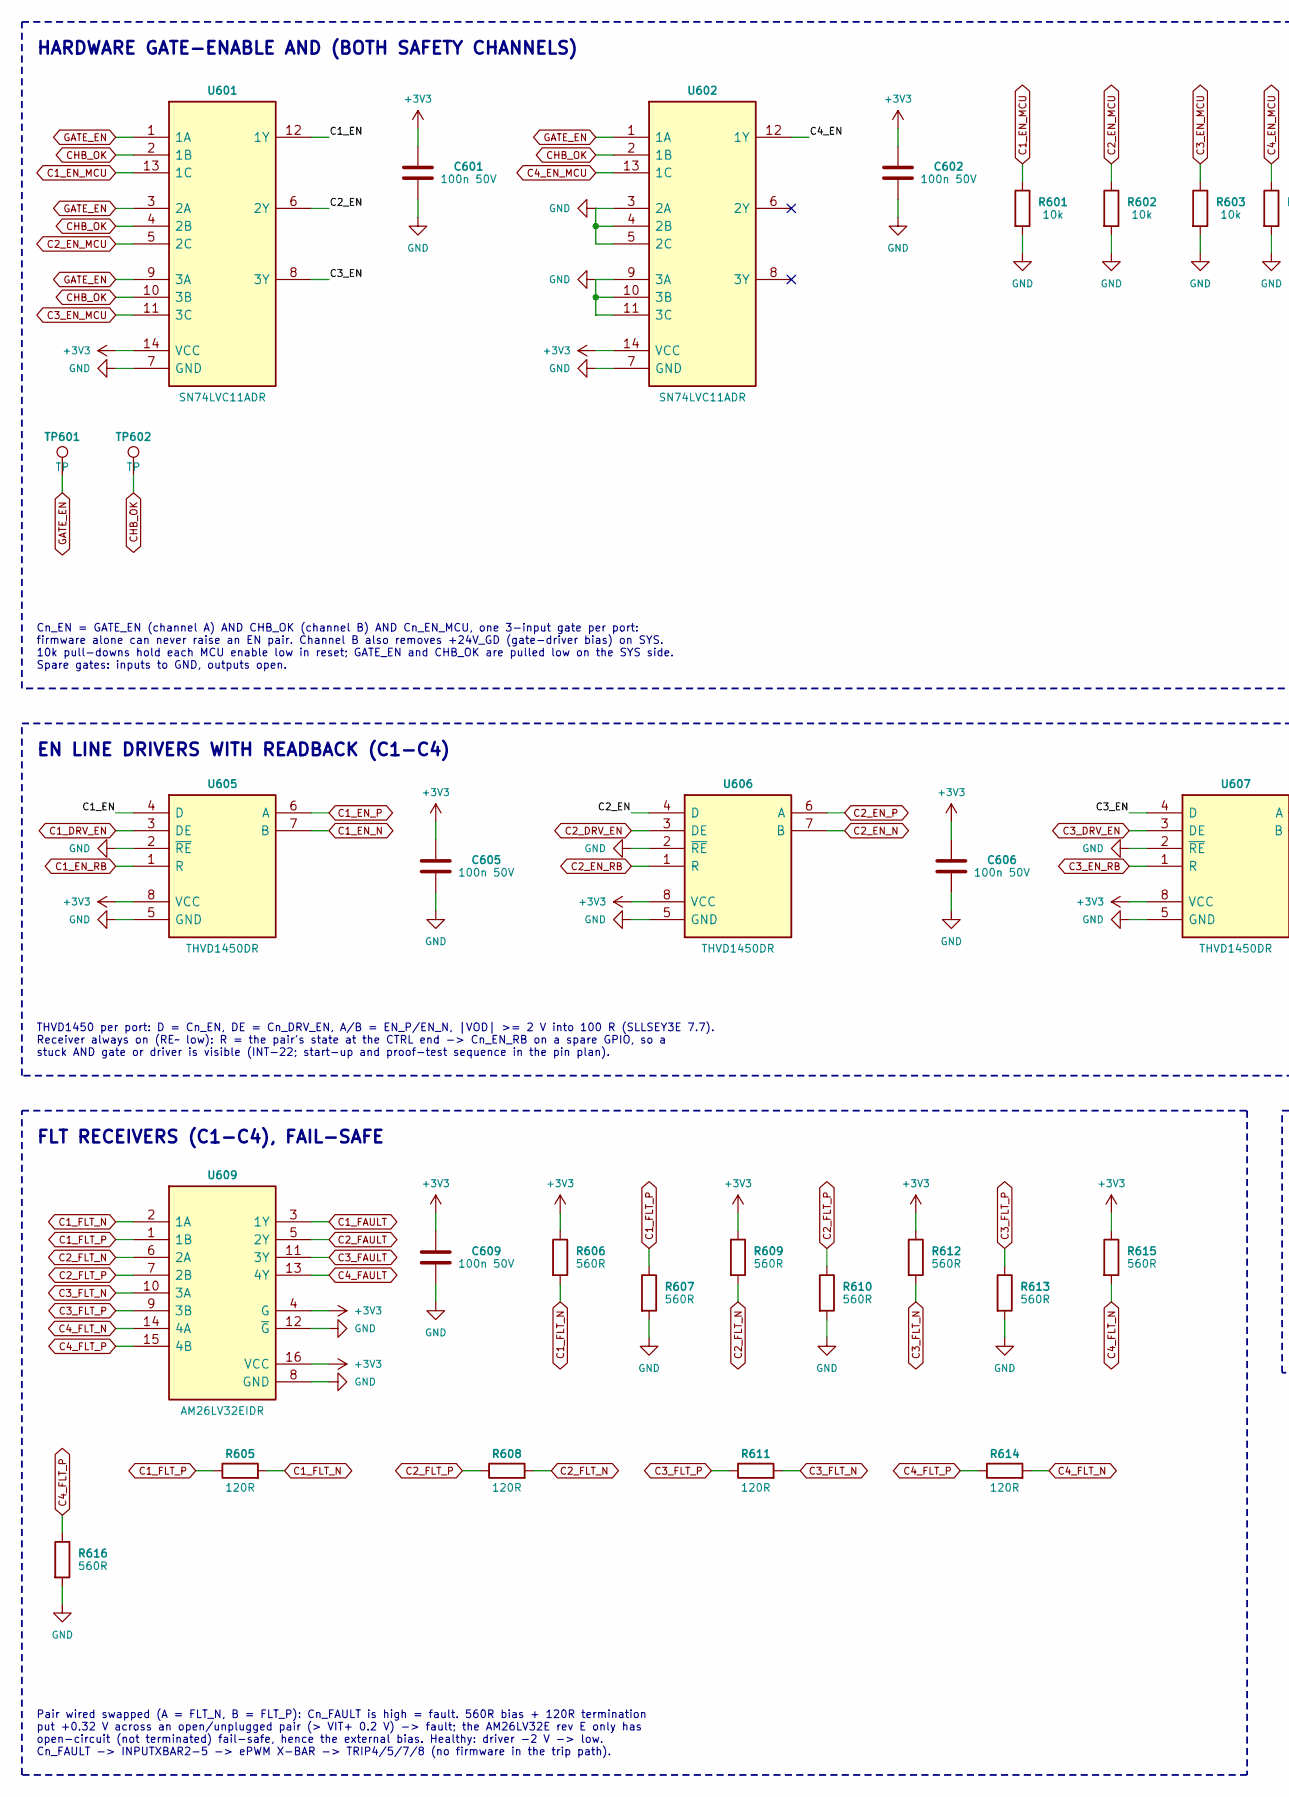
[picture p193: schematic 06_trip.kicad_sch, part in row 1, column 1]

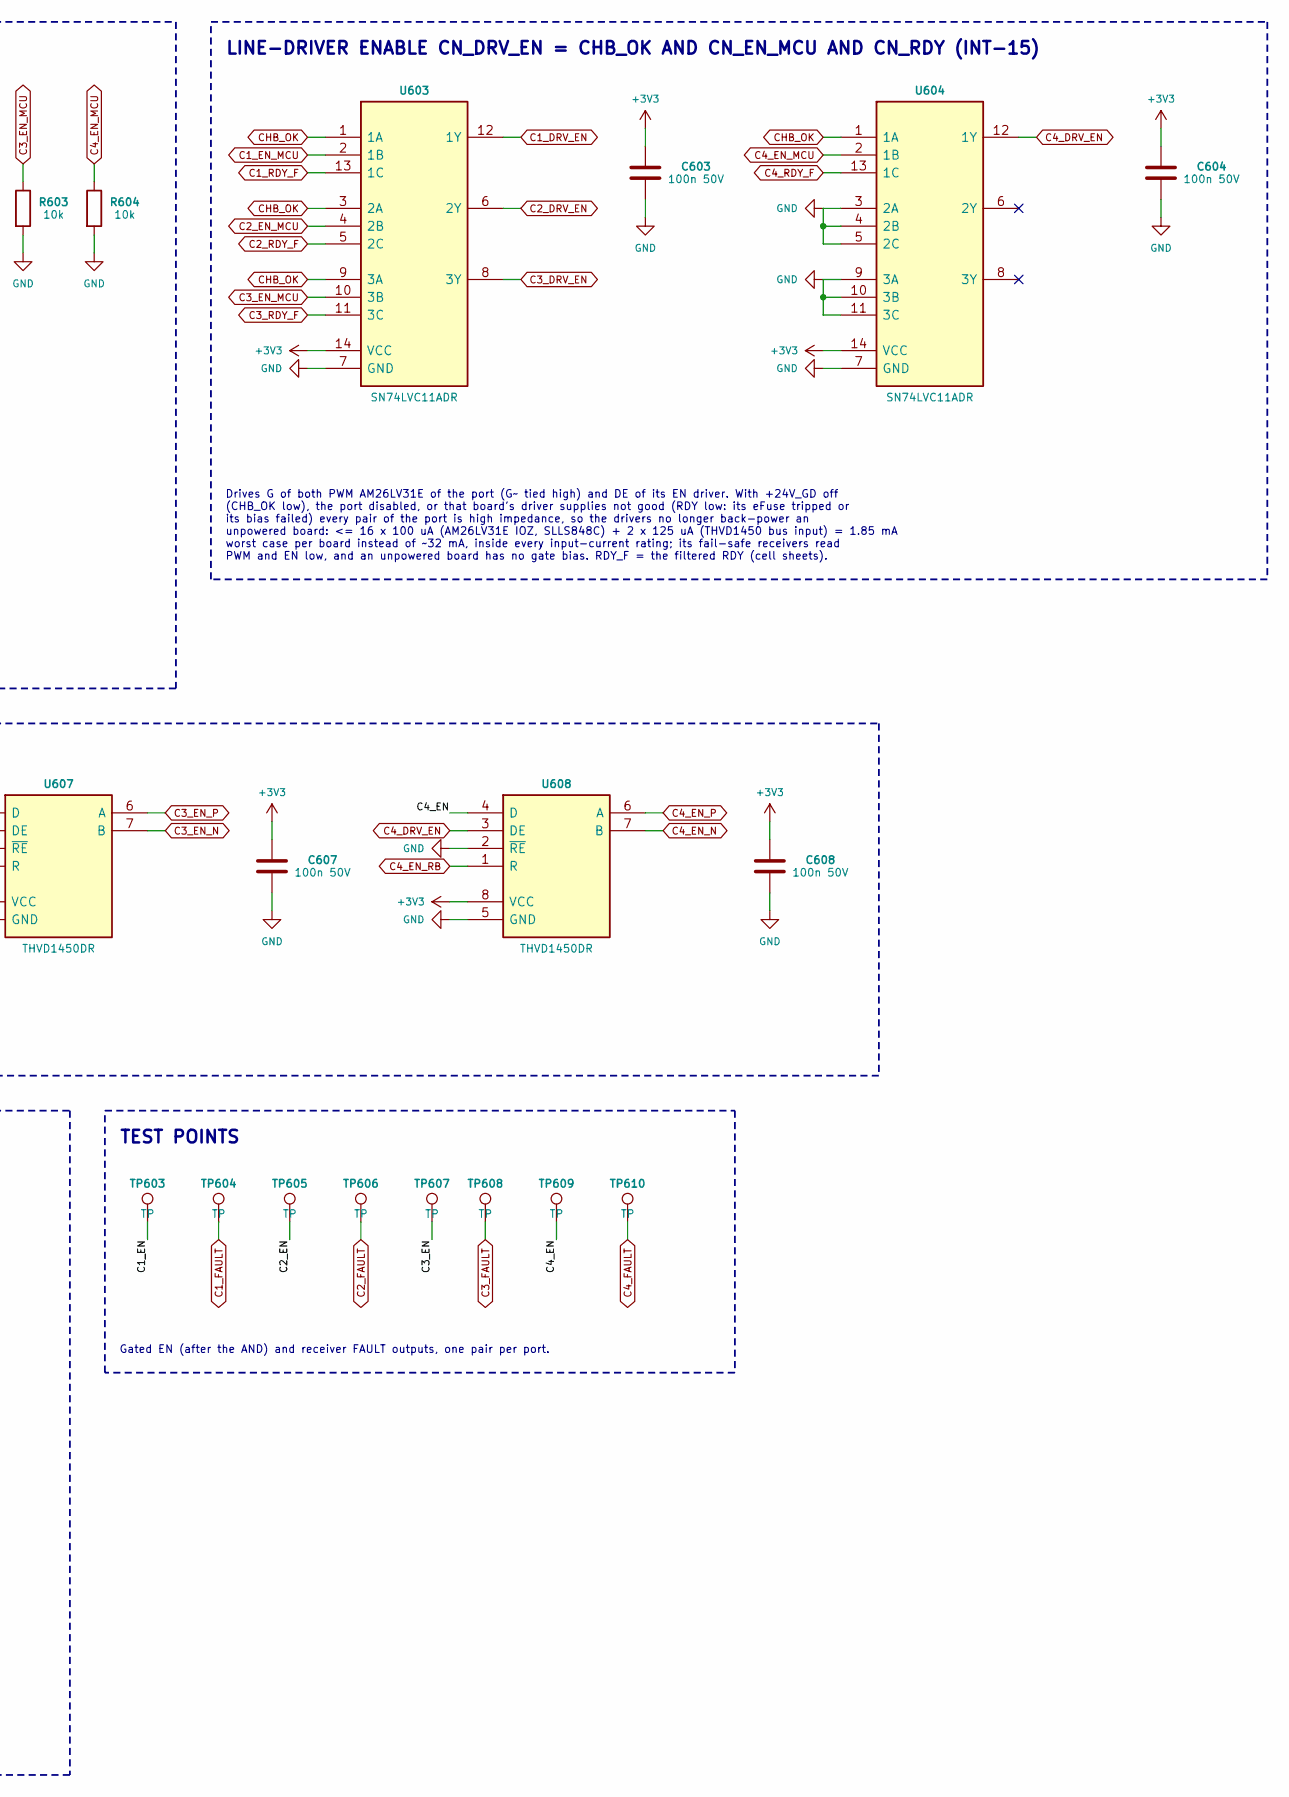
[picture p194: schematic 06_trip.kicad_sch, part in row 1, column 2]

Parts:
C601, C602, C603, C604, C605, C606, C607, C608, C609: 100n 50V
R601, R602, R603, R604: 10k
R605, R608, R611, R614: 120R
R606, R607, R609, R610, R612, R613, R615, R616: 560R
TP601, TP602, TP603, TP604, TP605, TP606, TP607, TP608, TP609, TP610: TP
U601, U602, U603, U604: SN74LVC11ADR; MPN SN74LVC11ADR
U605, U606, U607, U608: THVD1450DR; MPN THVD1450DR
U609: AM26LV32EIDR; MPN AM26LV32EIDR

Connections:
+3V3: C601.1, C602.1, C603.1, C604.1, C605.1, C606.1, C607.1, C608.1, C609.1, R606.1, R609.1, R612.1, R615.1, U601.14 (VCC), U602.14 (VCC), U603.14 (VCC), U604.14 (VCC), U605.8 (VCC), U606.8 (VCC), U607.8 (VCC), U608.8 (VCC), U609.4 (G), U609.16 (VCC)
C1_DRV_EN: U603.12 (1Y), U605.3 (DE)
C1_EN: TP603.1, U601.12 (1Y), U605.4 (D)
C1_EN_MCU: R601.1, U601.13 (1C), U603.2 (1B)
C1_EN_N: U605.7 (B)
C1_EN_P: U605.6 (A)
C1_EN_RB: U605.1 (R)
C1_FAULT: TP604.1, U609.3 (1Y)
C1_FLT_N: R605.2, R606.2, U609.2 (1A)
C1_FLT_P: R605.1, R607.1, U609.1 (1B)
C1_RDY_F: U603.13 (1C)
C2_DRV_EN: U603.6 (2Y), U606.3 (DE)
C2_EN: TP605.1, U601.6 (2Y), U606.4 (D)
C2_EN_MCU: R602.1, U601.5 (2C), U603.4 (2B)
C2_EN_N: U606.7 (B)
C2_EN_P: U606.6 (A)
C2_EN_RB: U606.1 (R)
C2_FAULT: TP606.1, U609.5 (2Y)
C2_FLT_N: R608.2, R609.2, U609.6 (2A)
C2_FLT_P: R608.1, R610.1, U609.7 (2B)
C2_RDY_F: U603.5 (2C)
C3_DRV_EN: U603.8 (3Y), U607.3 (DE)
C3_EN: TP607.1, U601.8 (3Y), U607.4 (D)
C3_EN_MCU: R603.1, U601.11 (3C), U603.10 (3B)
C3_EN_N: U607.7 (B)
C3_EN_P: U607.6 (A)
C3_EN_RB: U607.1 (R)
C3_FAULT: TP608.1, U609.11 (3Y)
C3_FLT_N: R611.2, R612.2, U609.10 (3A)
C3_FLT_P: R611.1, R613.1, U609.9 (3B)
C3_RDY_F: U603.11 (3C)
C4_DRV_EN: U604.12 (1Y), U608.3 (DE)
C4_EN: TP609.1, U602.12 (1Y), U608.4 (D)
C4_EN_MCU: R604.1, U602.13 (1C), U604.2 (1B)
C4_EN_N: U608.7 (B)
C4_EN_P: U608.6 (A)
C4_EN_RB: U608.1 (R)
C4_FAULT: TP610.1, U609.13 (4Y)
C4_FLT_N: R614.2, R615.2, U609.14 (4A)
C4_FLT_P: R614.1, R616.1, U609.15 (4B)
C4_RDY_F: U604.13 (1C)
CHB_OK: TP602.1, U601.2 (1B), U601.4 (2B), U601.10 (3B), U602.2 (1B), U603.1 (1A), U603.3 (2A), U603.9 (3A), U604.1 (1A)
GATE_EN: TP601.1, U601.1 (1A), U601.3 (2A), U601.9 (3A), U602.1 (1A)
GND: C601.2, C602.2, C603.2, C604.2, C605.2, C606.2, C607.2, C608.2, C609.2, R601.2, R602.2, R603.2, R604.2, R607.2, R610.2, R613.2, R616.2, U601.7 (GND), U602.3 (2A), U602.4 (2B), U602.5 (2C), U602.7 (GND), U602.9 (3A), U602.10 (3B), U602.11 (3C), U603.7 (GND), U604.3 (2A), U604.4 (2B), U604.5 (2C), U604.7 (GND), U604.9 (3A), U604.10 (3B), U604.11 (3C), U605.2 (~RE), U605.5 (GND), U606.2 (~RE), U606.5 (GND), U607.2 (~RE), U607.5 (GND), U608.2 (~RE), U608.5 (GND), U609.8 (GND), U609.12 (~G)

Notes on the sheet:
Drives G of both PWM AM26LV31E of the port (G~ tied high) and DE of its EN driver. With +24V_GD off (CHB_OK low), the port disabled, or that board's driver supplies not good (RDY low: its eFuse tripped or its bias failed) every pair of the port is high impedance, so the drivers no longer back-power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
HARDWARE GATE-ENABLE AND (BOTH SAFETY CHANNELS)
THVD1450 per port: D = Cn_EN, DE = Cn_DRV_EN, A/B = EN_P/EN_N, |VOD| >= 2 V into 100 R (SLLSEY3E 7.7). Receiver always on (RE~ low): R = the pair's state at the CTRL end -> Cn_EN_RB on a spare GPIO, so a stuck AND gate or driver is visible (INT-22; start-up and proof-test sequence in the pin plan).
EN LINE DRIVERS WITH READBACK (C1-C4)
FLT RECEIVERS (C1-C4), FAIL-SAFE
TEST POINTS
Pair wired swapped (A = FLT_N, B = FLT_P): Cn_FAULT is high = fault. 560R bias + 120R termination put +0.32 V across an open/unplugged pair (> VIT+ 0.2 V) -> fault; the AM26LV32E rev E only has open-circuit (not terminated) fail-safe, hence the external bias. Healthy: driver -2 V -> low. Cn_FAULT -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
Gated EN (after the AND) and receiver FAULT outputs, one pair per port.
LINE-DRIVER ENABLE CN_DRV_EN = CHB_OK AND CN_EN_MCU AND CN_RDY (INT-15)
Cn_EN = GATE_EN (channel A) AND CHB_OK (channel B) AND Cn_EN_MCU, one 3-input gate per port: firmware alone can never raise an EN pair. Channel B also removes +24V_GD (gate-driver bias) on SYS. 10k pull-downs hold each MCU enable low in reset; GATE_EN and CHB_OK are pulled low on the SYS side. Spar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
