vectivolt/PCM/hardware/CTRL-C2000/sheets/07_cell1.kicad_sch

## KiCad design hardware/CTRL-C2000/sheets/07_cell1.kicad_sch (2026-10-04)

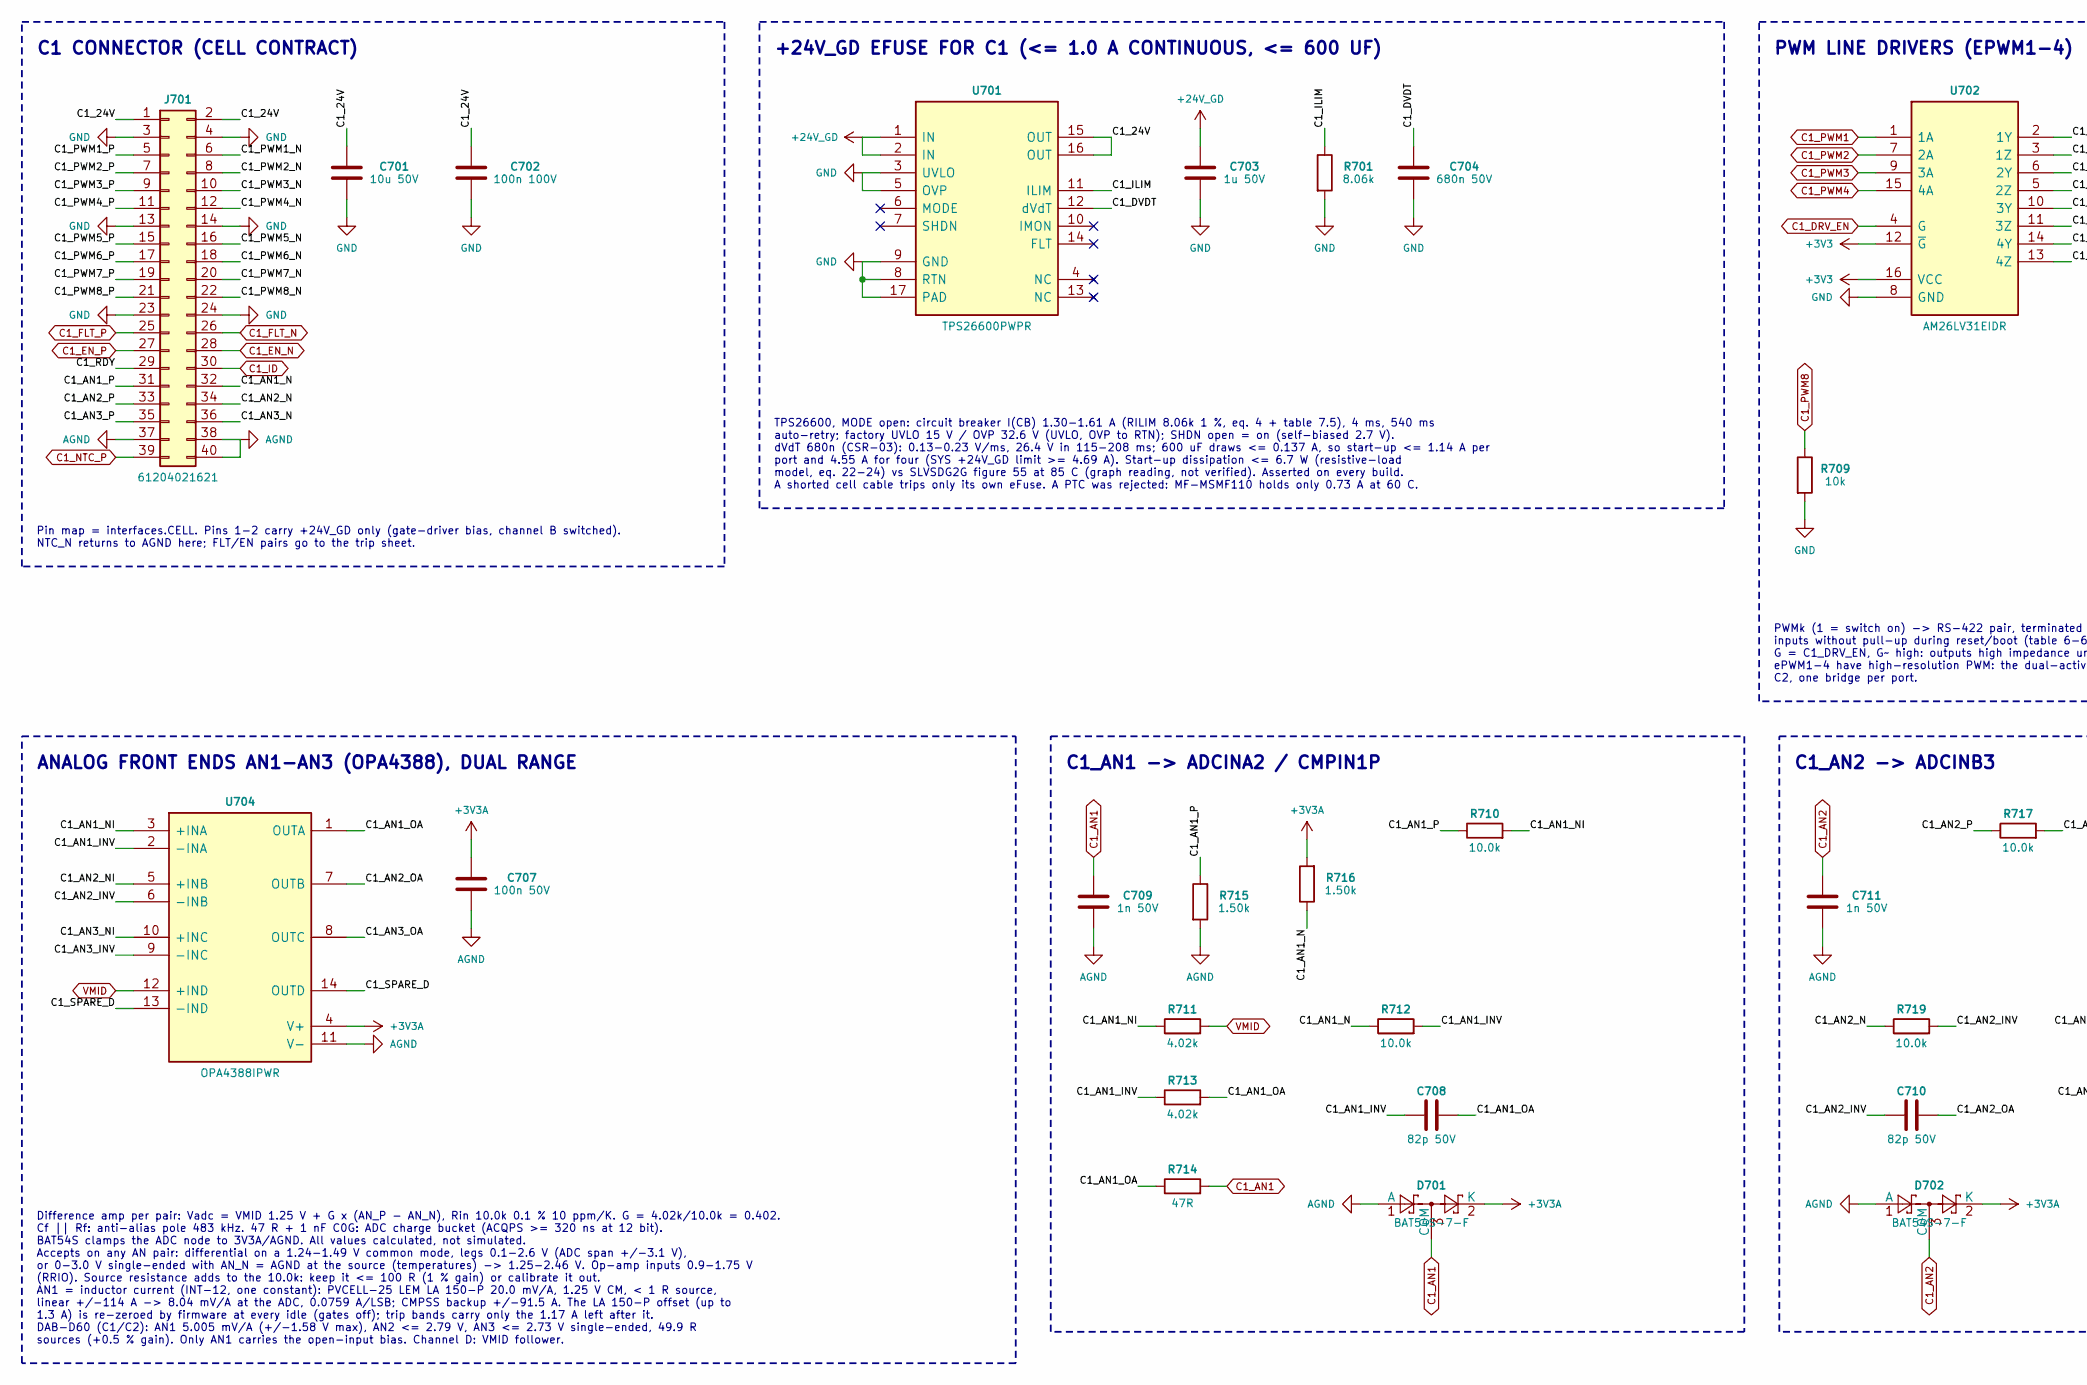
[picture p195: schematic 07_cell1.kicad_sch, part in row 1, column 1]

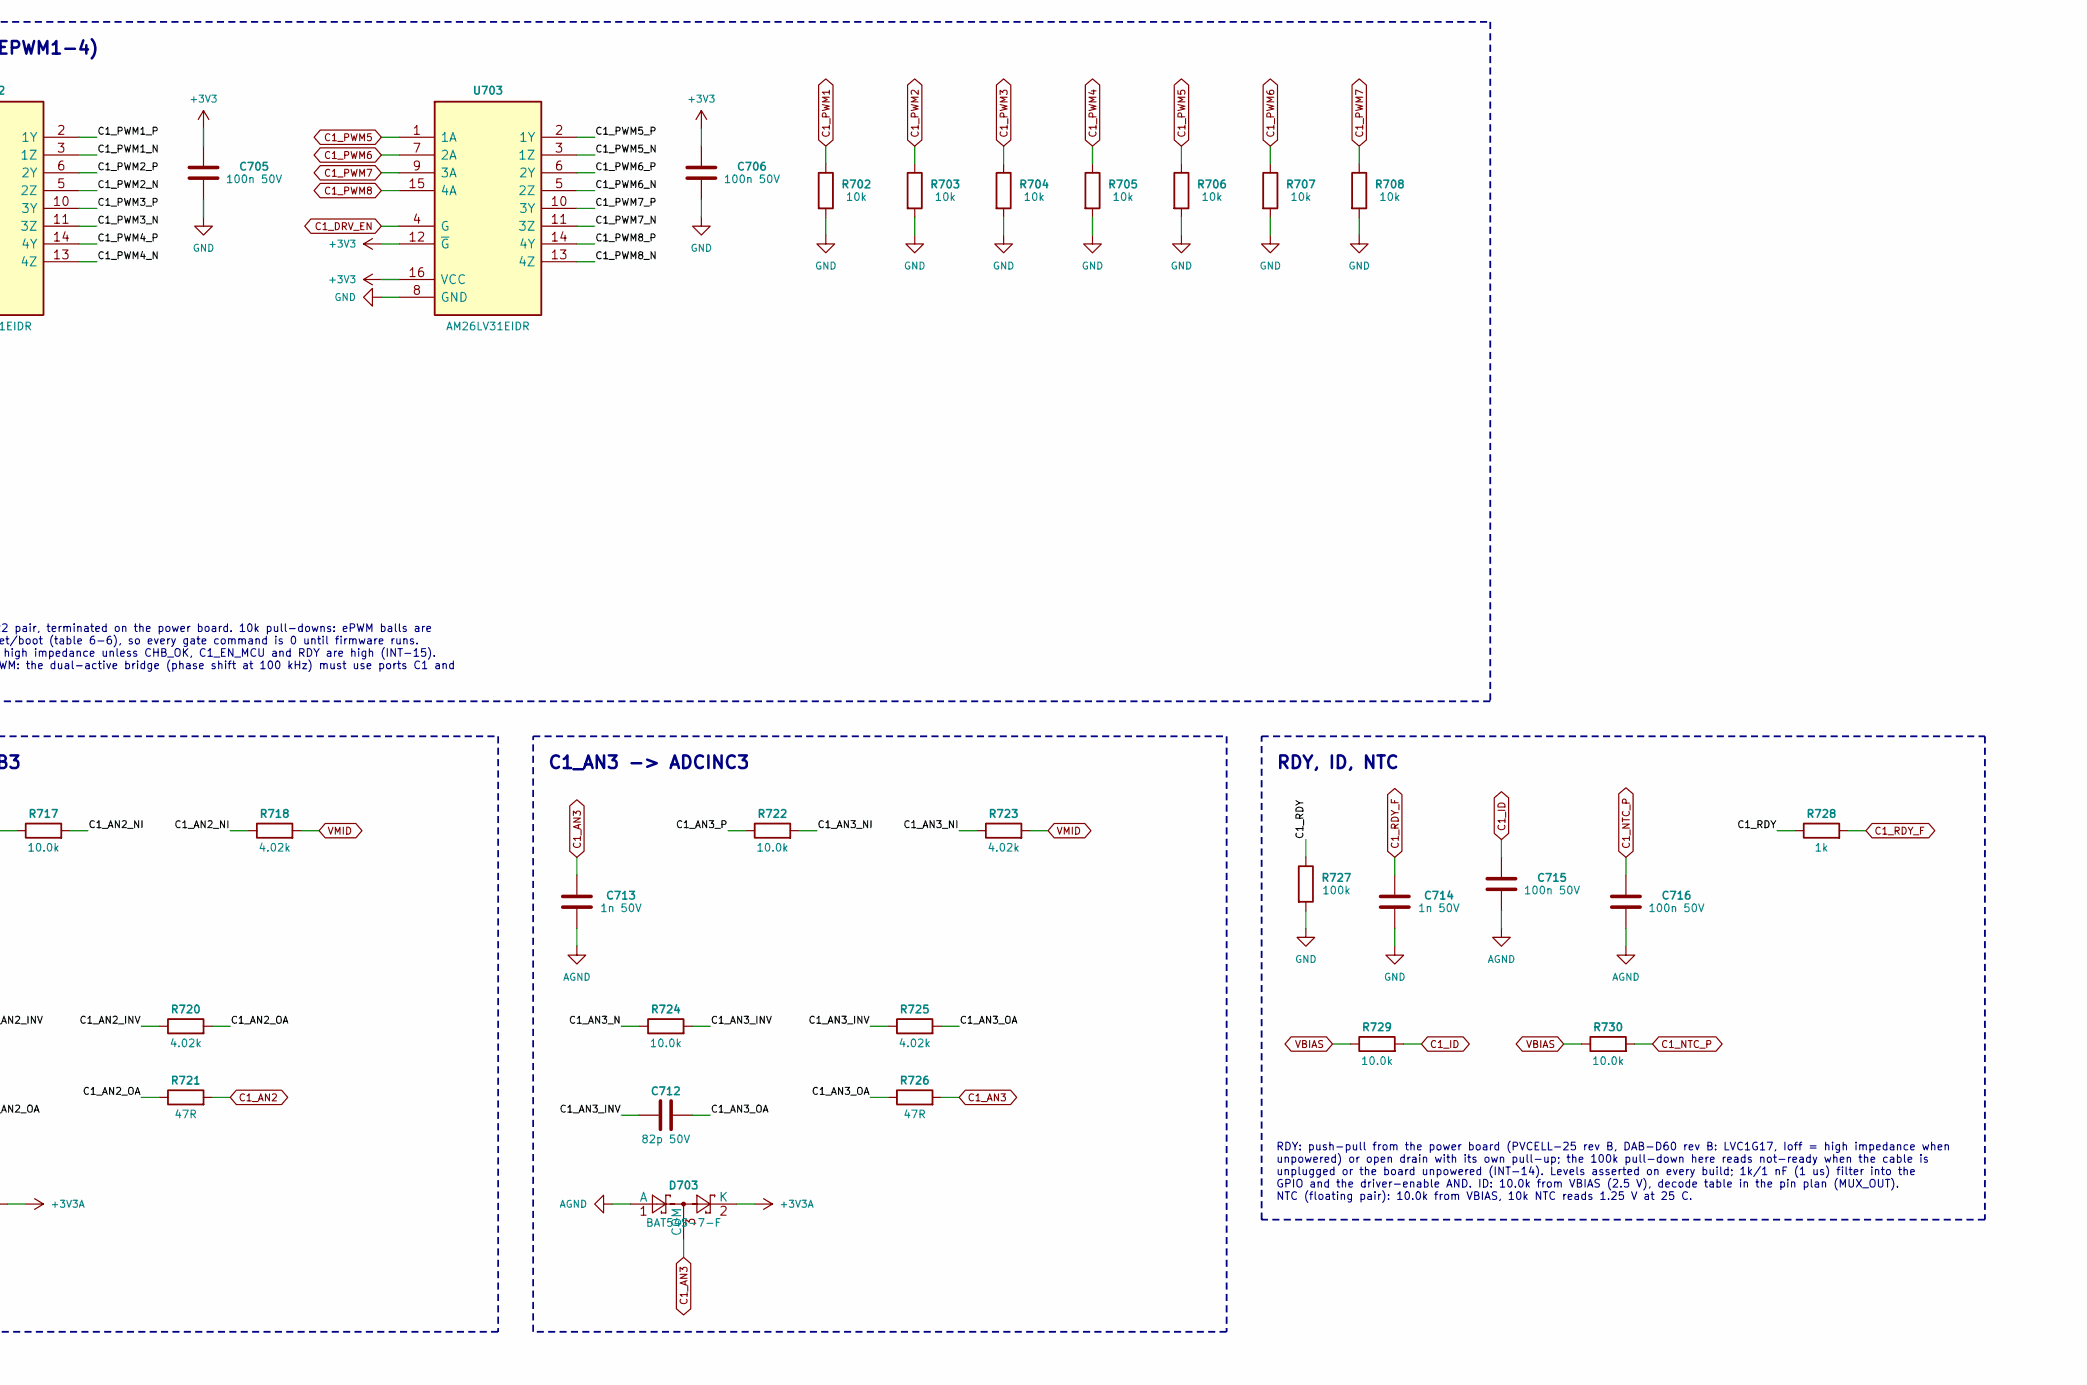
[picture p196: schematic 07_cell1.kicad_sch, part in row 1, column 2]

Parts:
C701: 10u 50V
C702: 100n 100V
C703: 1u 50V
C704: 680n 50V
C705, C706, C707, C715, C716: 100n 50V
C708, C710, C712: 82p 50V
C709, C711, C713, C714: 1n 50V
D701, D702, D703: BAT54S-7-F; MPN BAT54S-7-F
J701: 61204021621; MPN 61204021621
R701: 8.06k
R702, R703, R704, R705, R706, R707, R708, R709: 10k
R710, R712, R717, R719, R722, R724, R729, R730: 10.0k
R711, R713, R718, R720, R723, R725: 4.02k
R714, R721, R726: 47R
R715, R716: 1.50k
R727: 100k
R728: 1k
U701: TPS26600PWPR; MPN TPS26600PWPR
U702, U703: AM26LV31EIDR; MPN AM26LV31EIDR
U704: OPA4388IPWR; MPN OPA4388IPWR

Connections:
+3V3: C705.1, C706.1, U702.12 (~G), U702.16 (VCC), U703.12 (~G), U703.16 (VCC)
+3V3A: C707.1, D701.2 (K), D702.2 (K), D703.2 (K), R716.2, U704.4 (V+)
+24V_GD: C703.1, U701.1 (IN), U701.2 (IN)
AGND: C707.2, C709.2, C711.2, C713.2, C715.2, C716.2, D701.1 (A), D702.1 (A), D703.1 (A), J701.37, J701.38, J701.40, R715.2, U704.11 (V-)
C1_24V: C701.1, C702.1, J701.1, J701.2, U701.15 (OUT), U701.16 (OUT)
C1_AN1: C709.1, D701.3 (COM), R714.2
C1_AN1_INV: C708.1, R712.2, R713.1, U704.2 (-INA)
C1_AN1_N: J701.32, R712.1, R716.1
C1_AN1_NI: R710.2, R711.1, U704.3 (+INA)
C1_AN1_OA: C708.2, R713.2, R714.1, U704.1 (OUTA)
C1_AN1_P: J701.31, R710.1, R715.1
C1_AN2: C711.1, D702.3 (COM), R721.2
C1_AN2_INV: C710.1, R719.2, R720.1, U704.6 (-INB)
C1_AN2_N: J701.34, R719.1
C1_AN2_NI: R717.2, R718.1, U704.5 (+INB)
C1_AN2_OA: C710.2, R720.2, R721.1, U704.7 (OUTB)
C1_AN2_P: J701.33, R717.1
C1_AN3: C713.1, D703.3 (COM), R726.2
C1_AN3_INV: C712.1, R724.2, R725.1, U704.9 (-INC)
C1_AN3_N: J701.36, R724.1
C1_AN3_NI: R722.2, R723.1, U704.10 (+INC)
C1_AN3_OA: C712.2, R725.2, R726.1, U704.8 (OUTC)
C1_AN3_P: J701.35, R722.1
C1_DRV_EN: U702.4 (G), U703.4 (G)
C1_DVDT: C704.1, U701.12 (dVdT)
C1_EN_N: J701.28
C1_EN_P: J701.27
C1_FLT_N: J701.26
C1_FLT_P: J701.25
C1_ID: C715.1, J701.30, R729.2
C1_ILIM: R701.1, U701.11 (ILIM)
C1_NTC_P: C716.1, J701.39, R730.2
C1_PWM1: R702.1, U702.1 (1A)
C1_PWM1_N: J701.6, U702.3 (1Z)
C1_PWM1_P: J701.5, U702.2 (1Y)
C1_PWM2: R703.1, U702.7 (2A)
C1_PWM2_N: J701.8, U702.5 (2Z)
C1_PWM2_P: J701.7, U702.6 (2Y)
C1_PWM3: R704.1, U702.9 (3A)
C1_PWM3_N: J701.10, U702.11 (3Z)
C1_PWM3_P: J701.9, U702.10 (3Y)
C1_PWM4: R705.1, U702.15 (4A)
C1_PWM4_N: J701.12, U702.13 (4Z)
C1_PWM4_P: J701.11, U702.14 (4Y)
C1_PWM5: R706.1, U703.1 (1A)
C1_PWM5_N: J701.16, U703.3 (1Z)
C1_PWM5_P: J701.15, U703.2 (1Y)
C1_PWM6: R707.1, U703.7 (2A)
C1_PWM6_N: J701.18, U703.5 (2Z)
C1_PWM6_P: J701.17, U703.6 (2Y)
C1_PWM7: R708.1, U703.9 (3A)
C1_PWM7_N: J701.20, U703.11 (3Z)
C1_PWM7_P: J701.19, U703.10 (3Y)
C1_PWM8: R709.1, U703.15 (4A)
C1_PWM8_N: J701.22, U703.13 (4Z)
C1_PWM8_P: J701.21, U703.14 (4Y)
C1_RDY: J701.29, R727.1, R728.1
C1_RDY_F: C714.1, R728.2
C1_SPARE_D: U704.13 (-IND), U704.14 (OUTD)
GND: C701.2, C702.2, C703.2, C704.2, C705.2, C706.2, C714.2, J701.3, J701.4, J701.13, J701.14, J701.23, J701.24, R701.2, R702.2, R703.2, R704.2, R705.2, R706.2, R707.2, R708.2, R709.2, R727.2, U701.3 (UVLO), U701.5 (OVP), U701.8 (RTN), U701.9 (GND), U701.17 (PAD), U702.8 (GND), U703.8 (GND)
VBIAS: R729.1, R730.1
VMID: R711.2, R718.2, R723.2, U704.12 (+IND)

Notes on the sheet:
C1_AN2 -> ADCINB3
RDY: push-pull from the power board (PVCELL-25 rev B, DAB-D60 rev B: LVC1G17, Ioff = high impedance when unpowered) or open drain with its own pull-up; the 100k pull-down here reads not-ready when the cable is unplugged or the board unpowered (INT-14). Levels asserted on every build; 1k/1 nF (1 us)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
Pin map = interfaces.CELL. Pins 1-2 carry +24V_GD only (gate-driver bias, channel B switched). NTC_N returns to AGND here; FLT/EN pairs go to the trip sheet.
C1_AN1 -> ADCINA2 / CMPIN1P
C1 CONNECTOR (CELL CONTRACT)
PWM LINE DRIVERS (EPWM1-4)
+24V_GD EFUSE FOR C1 (<= 1.0 A CONTINUOUS, <= 600 UF)
PWMk (1 = switch on) -> RS-422 pair, terminated on the power board. 10k pull-downs: ePWM balls are inputs without pull-up during reset/boot (table 6-6), so every gate command is 0 until firmware runs. G = C1_DRV_EN, G~ high: outputs high impedance unless CHB_OK, C1_EN_MCU and RDY are high (INT-15).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
ANALOG FRONT ENDS AN1-AN3 (OPA4388), DUAL RANGE
C1_AN3 -> ADCINC3
Difference amp per pair: Vadc = VMID 1.25 V + G x (AN_P - AN_N), Rin 10.0k 0.1 % 10 ppm/K. G = 4.02k/10.0k = 0.402. Cf || Rf: anti-alias pole 483 kHz. 47 R + 1 nF C0G: ADC charge bucket (ACQPS >= 320 ns at 12 bit). BAT54S clamps the ADC node to 3V3A/AGND. All values calculated, not simulated. Accep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
TPS26600, MODE open: circuit breaker I(CB) 1.30-1.61 A (RILIM 8.06k 1 %, eq. 4 + table 7.5), 4 ms, 540 ms auto-retry; factory UVLO 15 V / OVP 32.6 V (UVLO, OVP to RTN); SHDN open = on (self-biased 2.7 V). dVdT 680n (CSR-03): 0.13-0.23 V/ms, 26.4 V in 115-208 ms; 600 uF draws <= 0.137 A, so start-up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
RDY, ID, NTC
