vectivolt/PCM/hardware/CTRL-C2000/sheets/08_cell2.kicad_sch

## KiCad design hardware/CTRL-C2000/sheets/08_cell2.kicad_sch (2026-10-04)

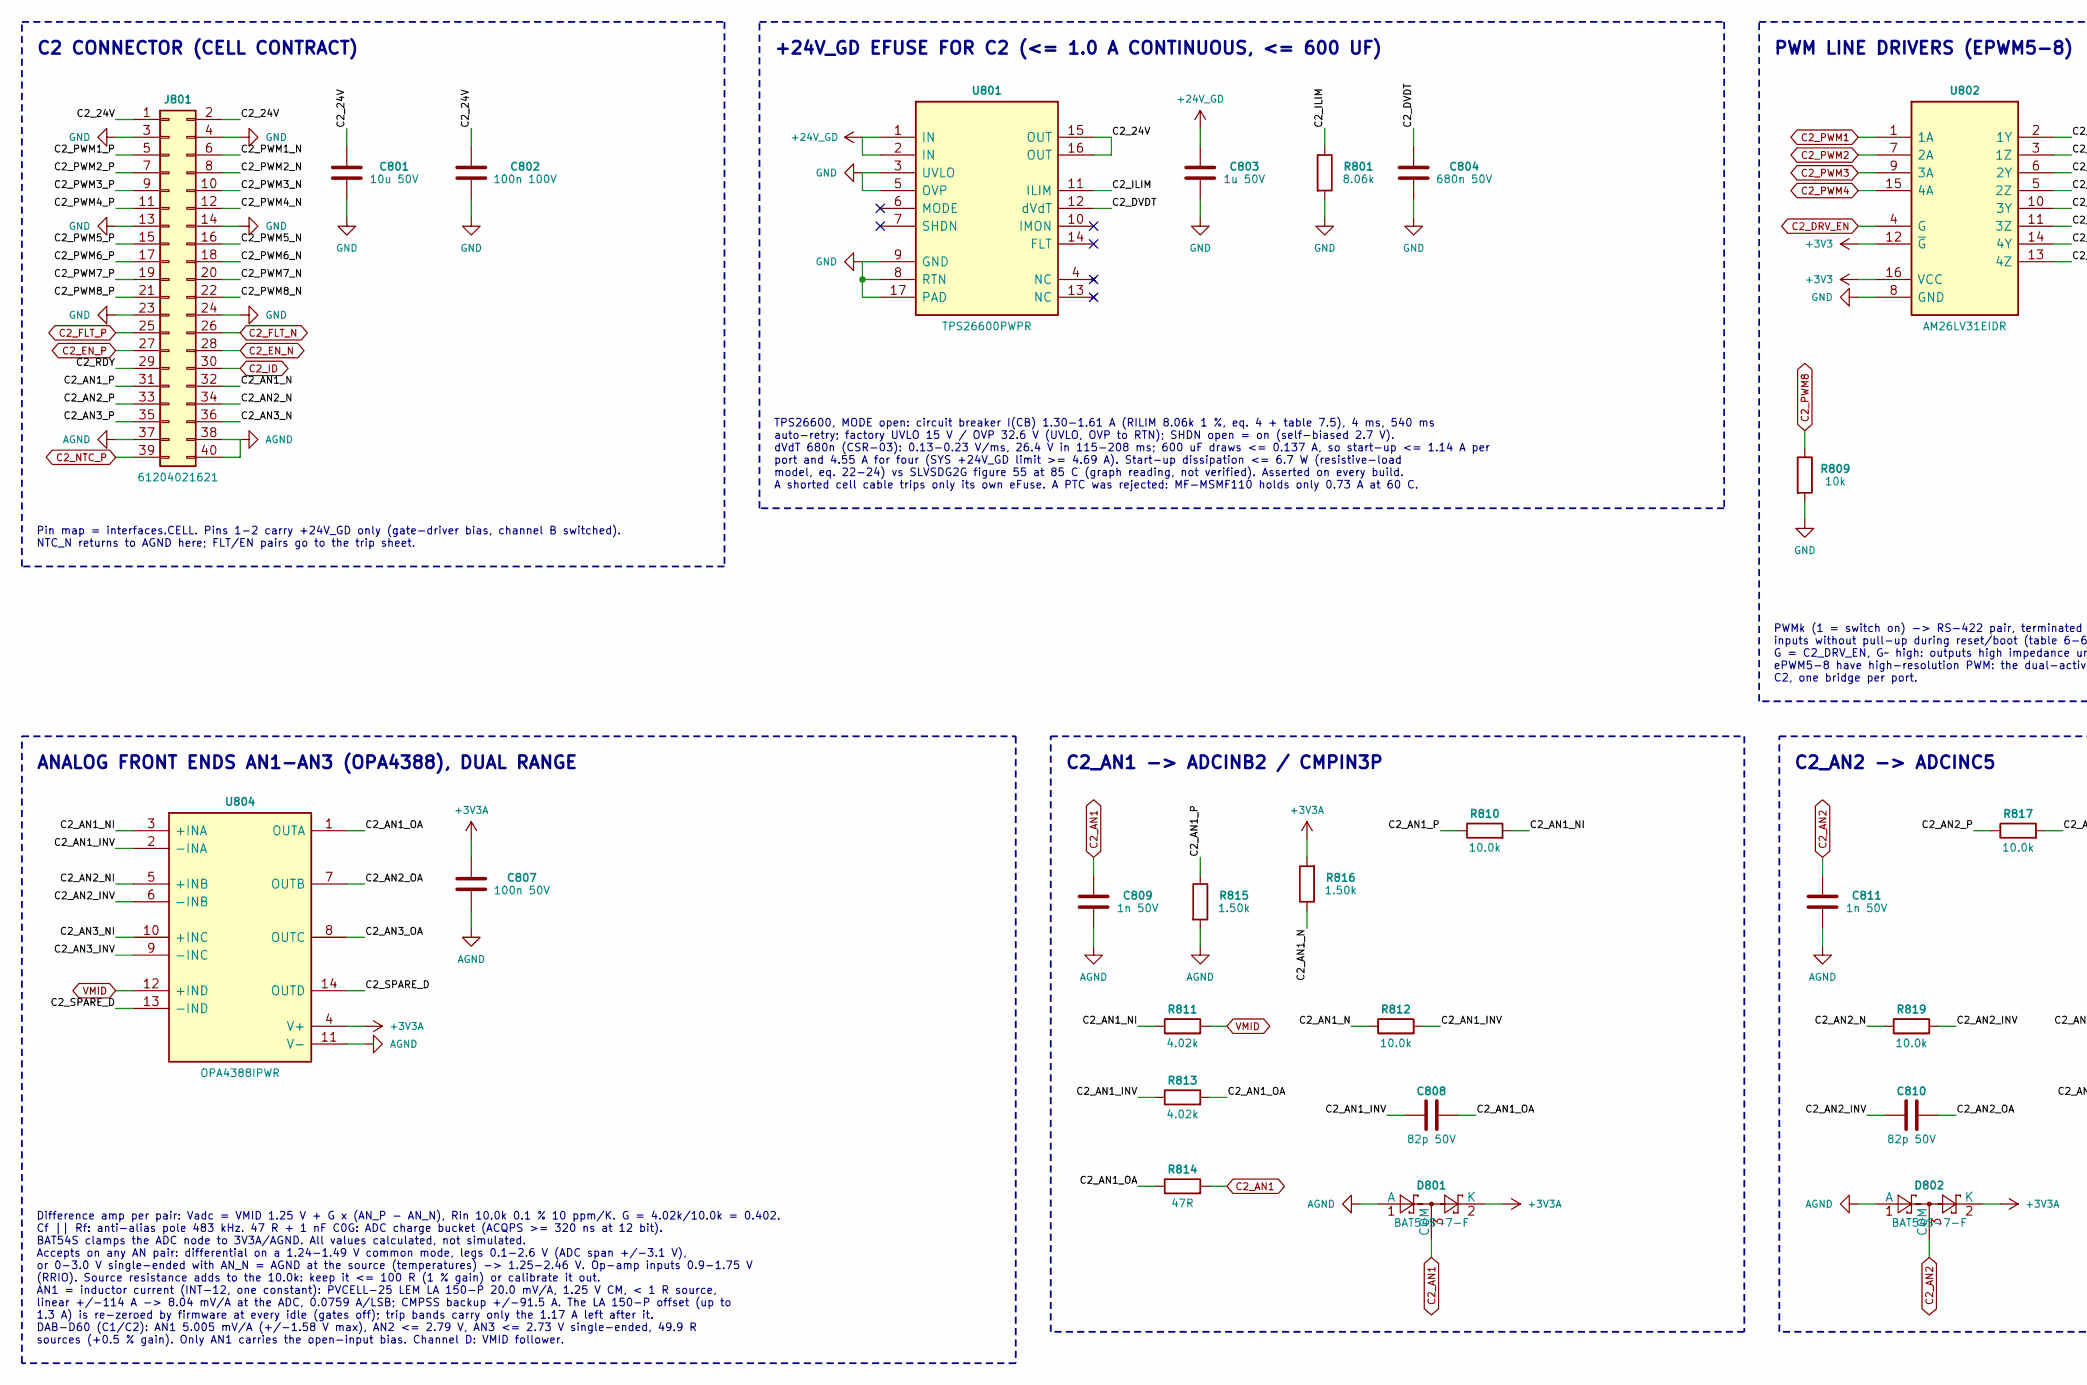
[picture p197: schematic 08_cell2.kicad_sch, part in row 1, column 1]

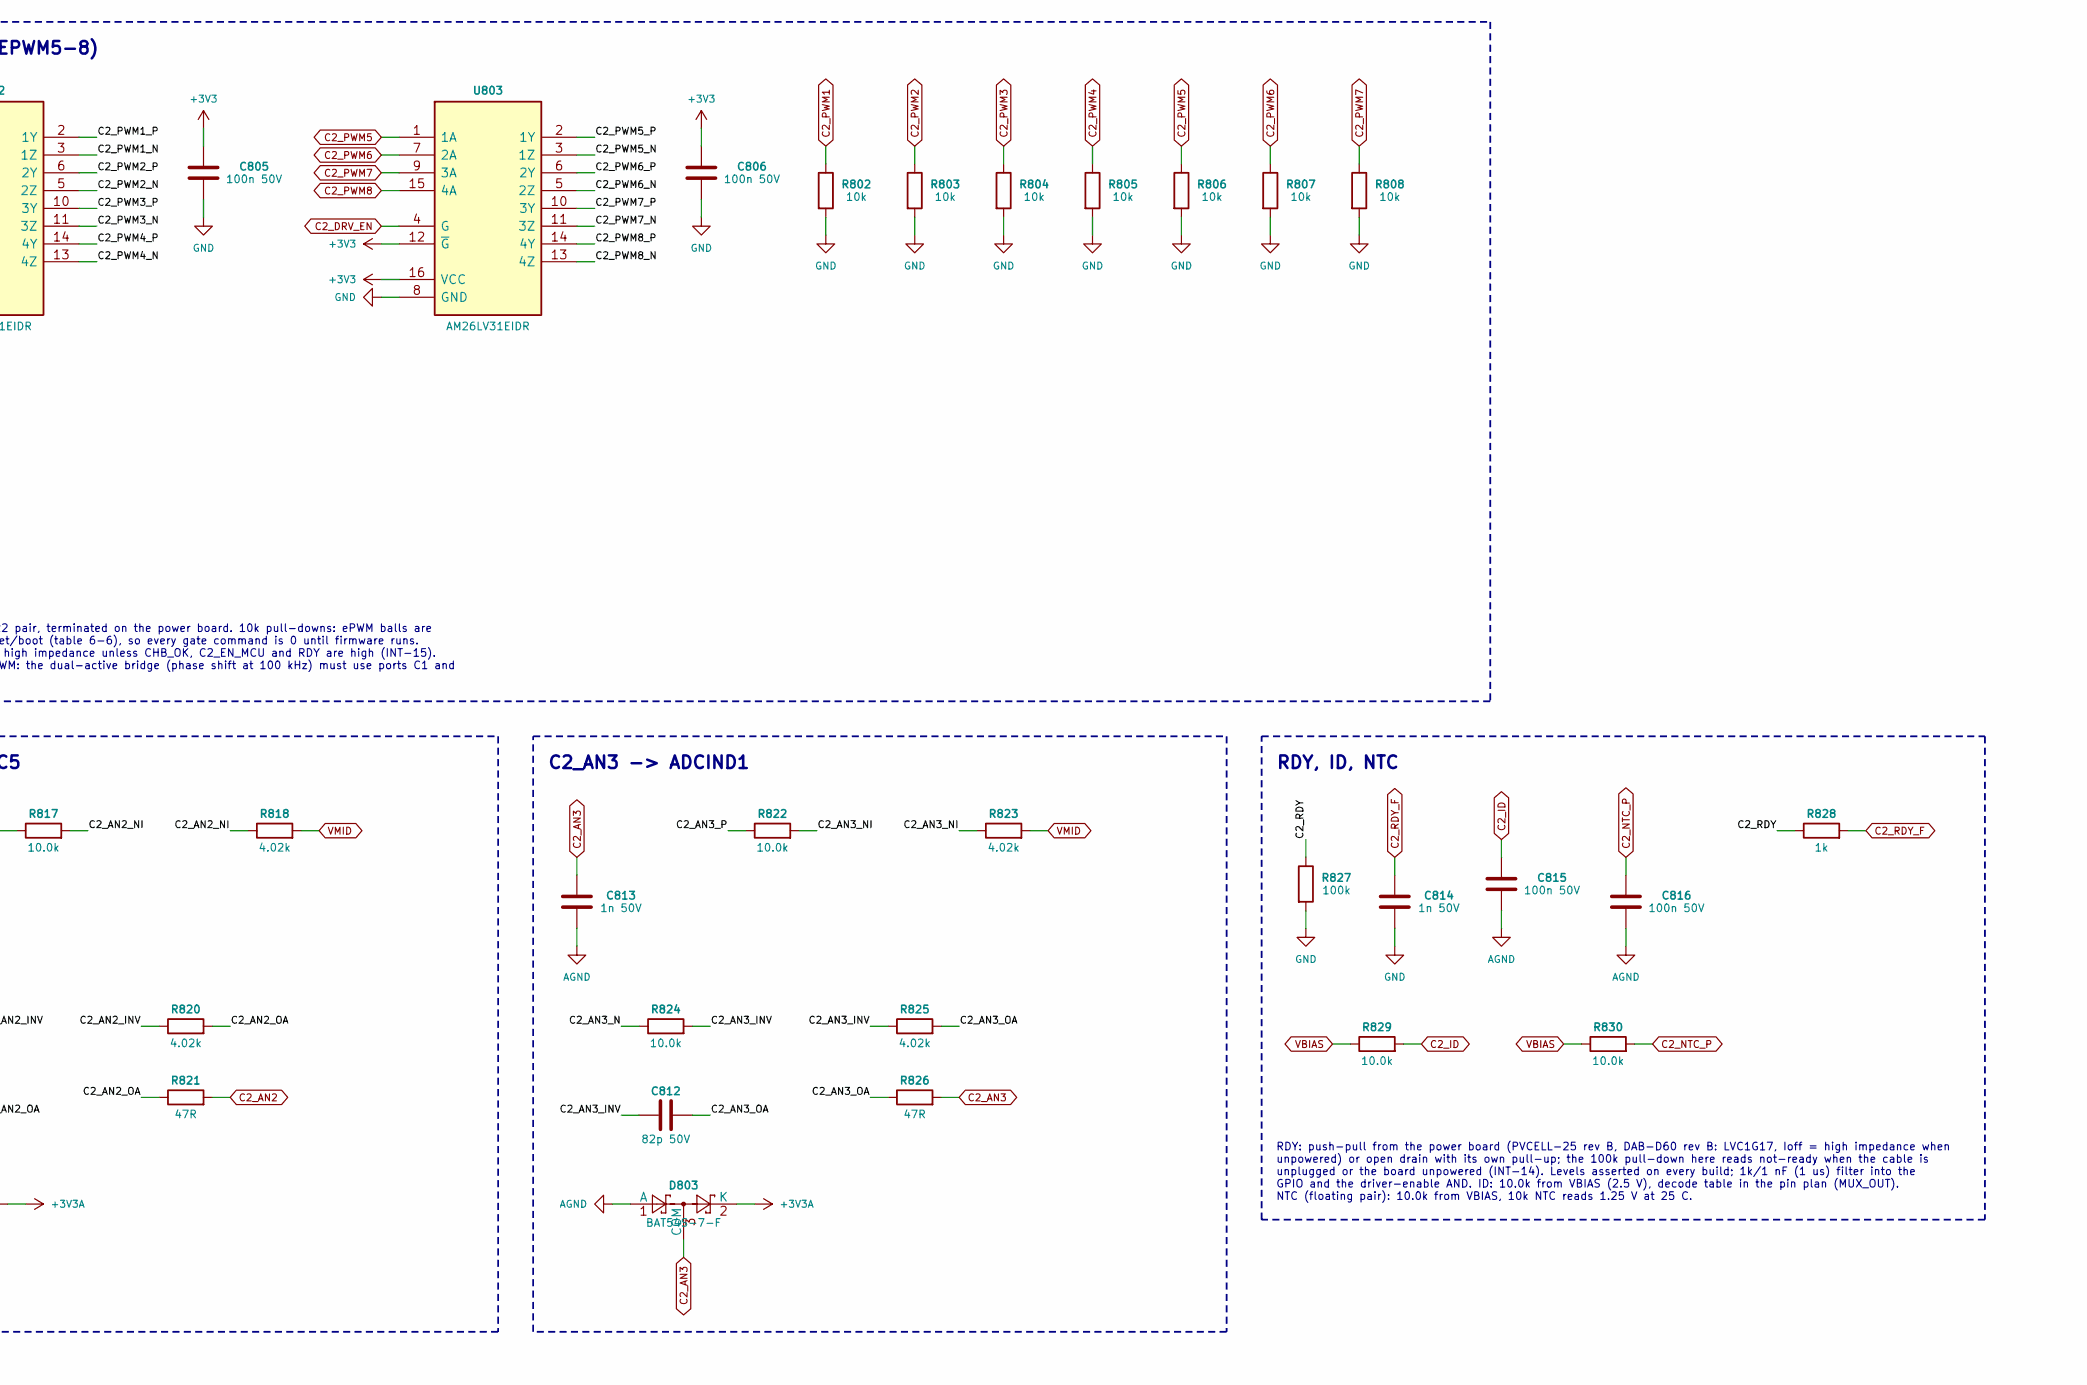
[picture p198: schematic 08_cell2.kicad_sch, part in row 1, column 2]

Parts:
C801: 10u 50V
C802: 100n 100V
C803: 1u 50V
C804: 680n 50V
C805, C806, C807, C815, C816: 100n 50V
C808, C810, C812: 82p 50V
C809, C811, C813, C814: 1n 50V
D801, D802, D803: BAT54S-7-F; MPN BAT54S-7-F
J801: 61204021621; MPN 61204021621
R801: 8.06k
R802, R803, R804, R805, R806, R807, R808, R809: 10k
R810, R812, R817, R819, R822, R824, R829, R830: 10.0k
R811, R813, R818, R820, R823, R825: 4.02k
R814, R821, R826: 47R
R815, R816: 1.50k
R827: 100k
R828: 1k
U801: TPS26600PWPR; MPN TPS26600PWPR
U802, U803: AM26LV31EIDR; MPN AM26LV31EIDR
U804: OPA4388IPWR; MPN OPA4388IPWR

Connections:
+3V3: C805.1, C806.1, U802.12 (~G), U802.16 (VCC), U803.12 (~G), U803.16 (VCC)
+3V3A: C807.1, D801.2 (K), D802.2 (K), D803.2 (K), R816.2, U804.4 (V+)
+24V_GD: C803.1, U801.1 (IN), U801.2 (IN)
AGND: C807.2, C809.2, C811.2, C813.2, C815.2, C816.2, D801.1 (A), D802.1 (A), D803.1 (A), J801.37, J801.38, J801.40, R815.2, U804.11 (V-)
C2_24V: C801.1, C802.1, J801.1, J801.2, U801.15 (OUT), U801.16 (OUT)
C2_AN1: C809.1, D801.3 (COM), R814.2
C2_AN1_INV: C808.1, R812.2, R813.1, U804.2 (-INA)
C2_AN1_N: J801.32, R812.1, R816.1
C2_AN1_NI: R810.2, R811.1, U804.3 (+INA)
C2_AN1_OA: C808.2, R813.2, R814.1, U804.1 (OUTA)
C2_AN1_P: J801.31, R810.1, R815.1
C2_AN2: C811.1, D802.3 (COM), R821.2
C2_AN2_INV: C810.1, R819.2, R820.1, U804.6 (-INB)
C2_AN2_N: J801.34, R819.1
C2_AN2_NI: R817.2, R818.1, U804.5 (+INB)
C2_AN2_OA: C810.2, R820.2, R821.1, U804.7 (OUTB)
C2_AN2_P: J801.33, R817.1
C2_AN3: C813.1, D803.3 (COM), R826.2
C2_AN3_INV: C812.1, R824.2, R825.1, U804.9 (-INC)
C2_AN3_N: J801.36, R824.1
C2_AN3_NI: R822.2, R823.1, U804.10 (+INC)
C2_AN3_OA: C812.2, R825.2, R826.1, U804.8 (OUTC)
C2_AN3_P: J801.35, R822.1
C2_DRV_EN: U802.4 (G), U803.4 (G)
C2_DVDT: C804.1, U801.12 (dVdT)
C2_EN_N: J801.28
C2_EN_P: J801.27
C2_FLT_N: J801.26
C2_FLT_P: J801.25
C2_ID: C815.1, J801.30, R829.2
C2_ILIM: R801.1, U801.11 (ILIM)
C2_NTC_P: C816.1, J801.39, R830.2
C2_PWM1: R802.1, U802.1 (1A)
C2_PWM1_N: J801.6, U802.3 (1Z)
C2_PWM1_P: J801.5, U802.2 (1Y)
C2_PWM2: R803.1, U802.7 (2A)
C2_PWM2_N: J801.8, U802.5 (2Z)
C2_PWM2_P: J801.7, U802.6 (2Y)
C2_PWM3: R804.1, U802.9 (3A)
C2_PWM3_N: J801.10, U802.11 (3Z)
C2_PWM3_P: J801.9, U802.10 (3Y)
C2_PWM4: R805.1, U802.15 (4A)
C2_PWM4_N: J801.12, U802.13 (4Z)
C2_PWM4_P: J801.11, U802.14 (4Y)
C2_PWM5: R806.1, U803.1 (1A)
C2_PWM5_N: J801.16, U803.3 (1Z)
C2_PWM5_P: J801.15, U803.2 (1Y)
C2_PWM6: R807.1, U803.7 (2A)
C2_PWM6_N: J801.18, U803.5 (2Z)
C2_PWM6_P: J801.17, U803.6 (2Y)
C2_PWM7: R808.1, U803.9 (3A)
C2_PWM7_N: J801.20, U803.11 (3Z)
C2_PWM7_P: J801.19, U803.10 (3Y)
C2_PWM8: R809.1, U803.15 (4A)
C2_PWM8_N: J801.22, U803.13 (4Z)
C2_PWM8_P: J801.21, U803.14 (4Y)
C2_RDY: J801.29, R827.1, R828.1
C2_RDY_F: C814.1, R828.2
C2_SPARE_D: U804.13 (-IND), U804.14 (OUTD)
GND: C801.2, C802.2, C803.2, C804.2, C805.2, C806.2, C814.2, J801.3, J801.4, J801.13, J801.14, J801.23, J801.24, R801.2, R802.2, R803.2, R804.2, R805.2, R806.2, R807.2, R808.2, R809.2, R827.2, U801.3 (UVLO), U801.5 (OVP), U801.8 (RTN), U801.9 (GND), U801.17 (PAD), U802.8 (GND), U803.8 (GND)
VBIAS: R829.1, R830.1
VMID: R811.2, R818.2, R823.2, U804.12 (+IND)

Notes on the sheet:
C2_AN1 -> ADCINB2 / CMPIN3P
TPS26600, MODE open: circuit breaker I(CB) 1.30-1.61 A (RILIM 8.06k 1 %, eq. 4 + table 7.5), 4 ms, 540 ms auto-retry; factory UVLO 15 V / OVP 32.6 V (UVLO, OVP to RTN); SHDN open = on (self-biased 2.7 V). dVdT 680n (CSR-03): 0.13-0.23 V/ms, 26.4 V in 115-208 ms; 600 uF draws <= 0.137 A, so start-up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
C2 CONNECTOR (CELL CONTRACT)
PWM LINE DRIVERS (EPWM5-8)
Difference amp per pair: Vadc = VMID 1.25 V + G x (AN_P - AN_N), Rin 10.0k 0.1 % 10 ppm/K. G = 4.02k/10.0k = 0.402. Cf || Rf: anti-alias pole 483 kHz. 47 R + 1 nF C0G: ADC charge bucket (ACQPS >= 320 ns at 12 bit). BAT54S clamps the ADC node to 3V3A/AGND. All values calculated, not simulated. Accep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
RDY: push-pull from the power board (PVCELL-25 rev B, DAB-D60 rev B: LVC1G17, Ioff = high impedance when unpowered) or open drain with its own pull-up; the 100k pull-down here reads not-ready when the cable is unplugged or the board unpowered (INT-14). Levels asserted on every build; 1k/1 nF (1 us)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
RDY, ID, NTC
C2_AN3 -> ADCIND1
+24V_GD EFUSE FOR C2 (<= 1.0 A CONTINUOUS, <= 600 UF)
ANALOG FRONT ENDS AN1-AN3 (OPA4388), DUAL RANGE
C2_AN2 -> ADCINC5
Pin map = interfaces.CELL. Pins 1-2 carry +24V_GD only (gate-driver bias, channel B switched). NTC_N returns to AGND here; FLT/EN pairs go to the trip sheet.
PWMk (1 = switch on) -> RS-422 pair, terminated on the power board. 10k pull-downs: ePWM balls are inputs without pull-up during reset/boot (table 6-6), so every gate command is 0 until firmware runs. G = C2_DRV_EN, G~ high: outputs high impedance unless CHB_OK, C2_EN_MCU and RDY are high (INT-15).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
