vectivolt/PCM/hardware/CTRL-C2000/sheets/09_cell3.kicad_sch

## KiCad design hardware/CTRL-C2000/sheets/09_cell3.kicad_sch (2026-10-04)

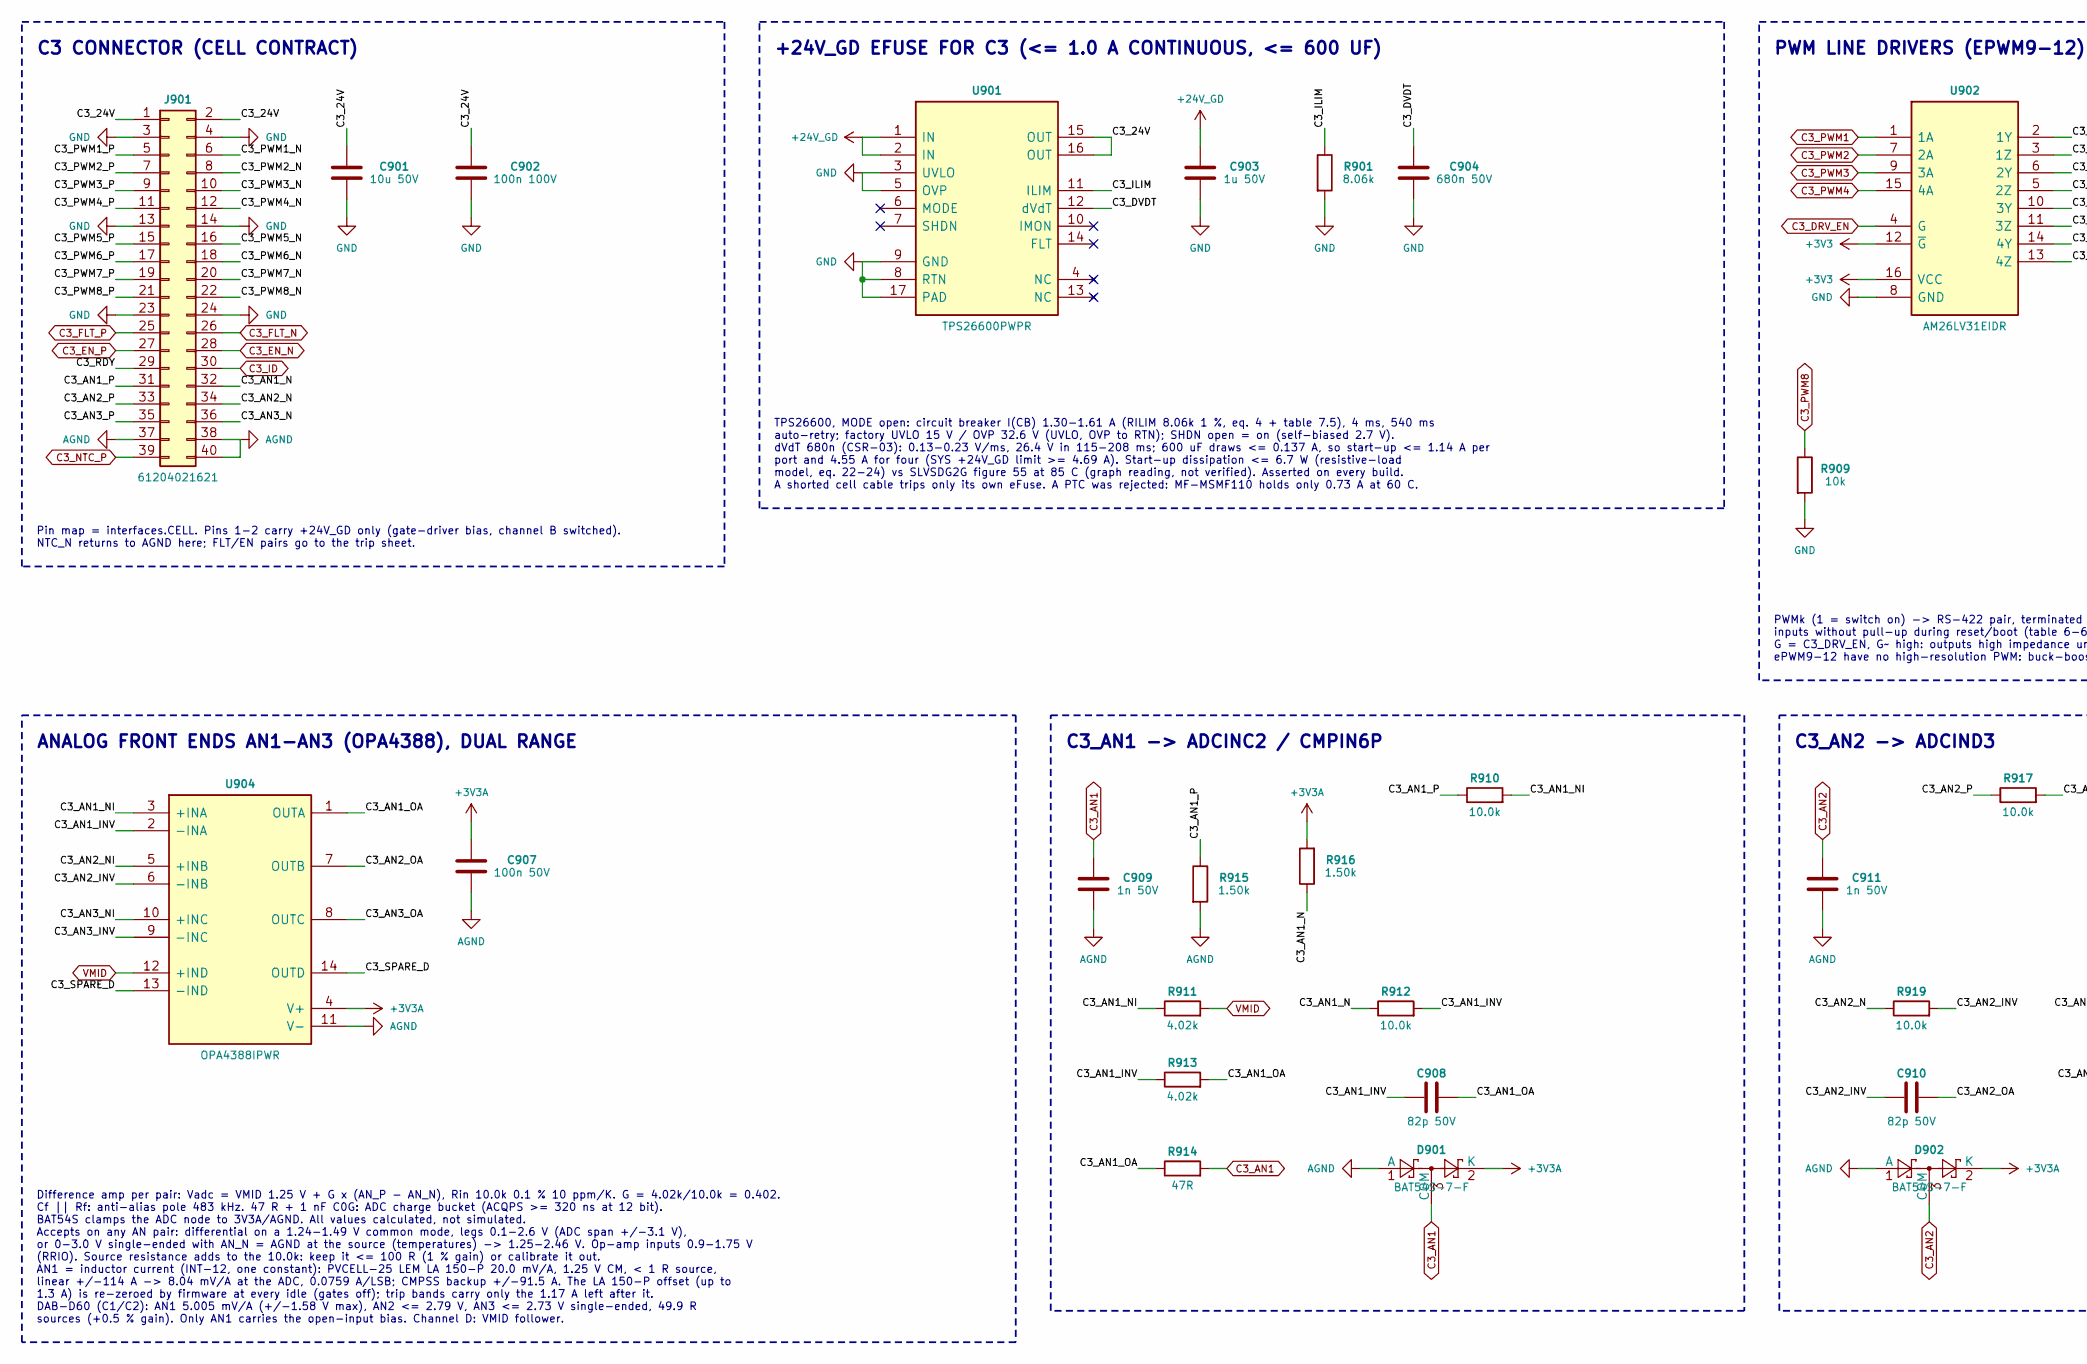
[picture p199: schematic 09_cell3.kicad_sch, part in row 1, column 1]

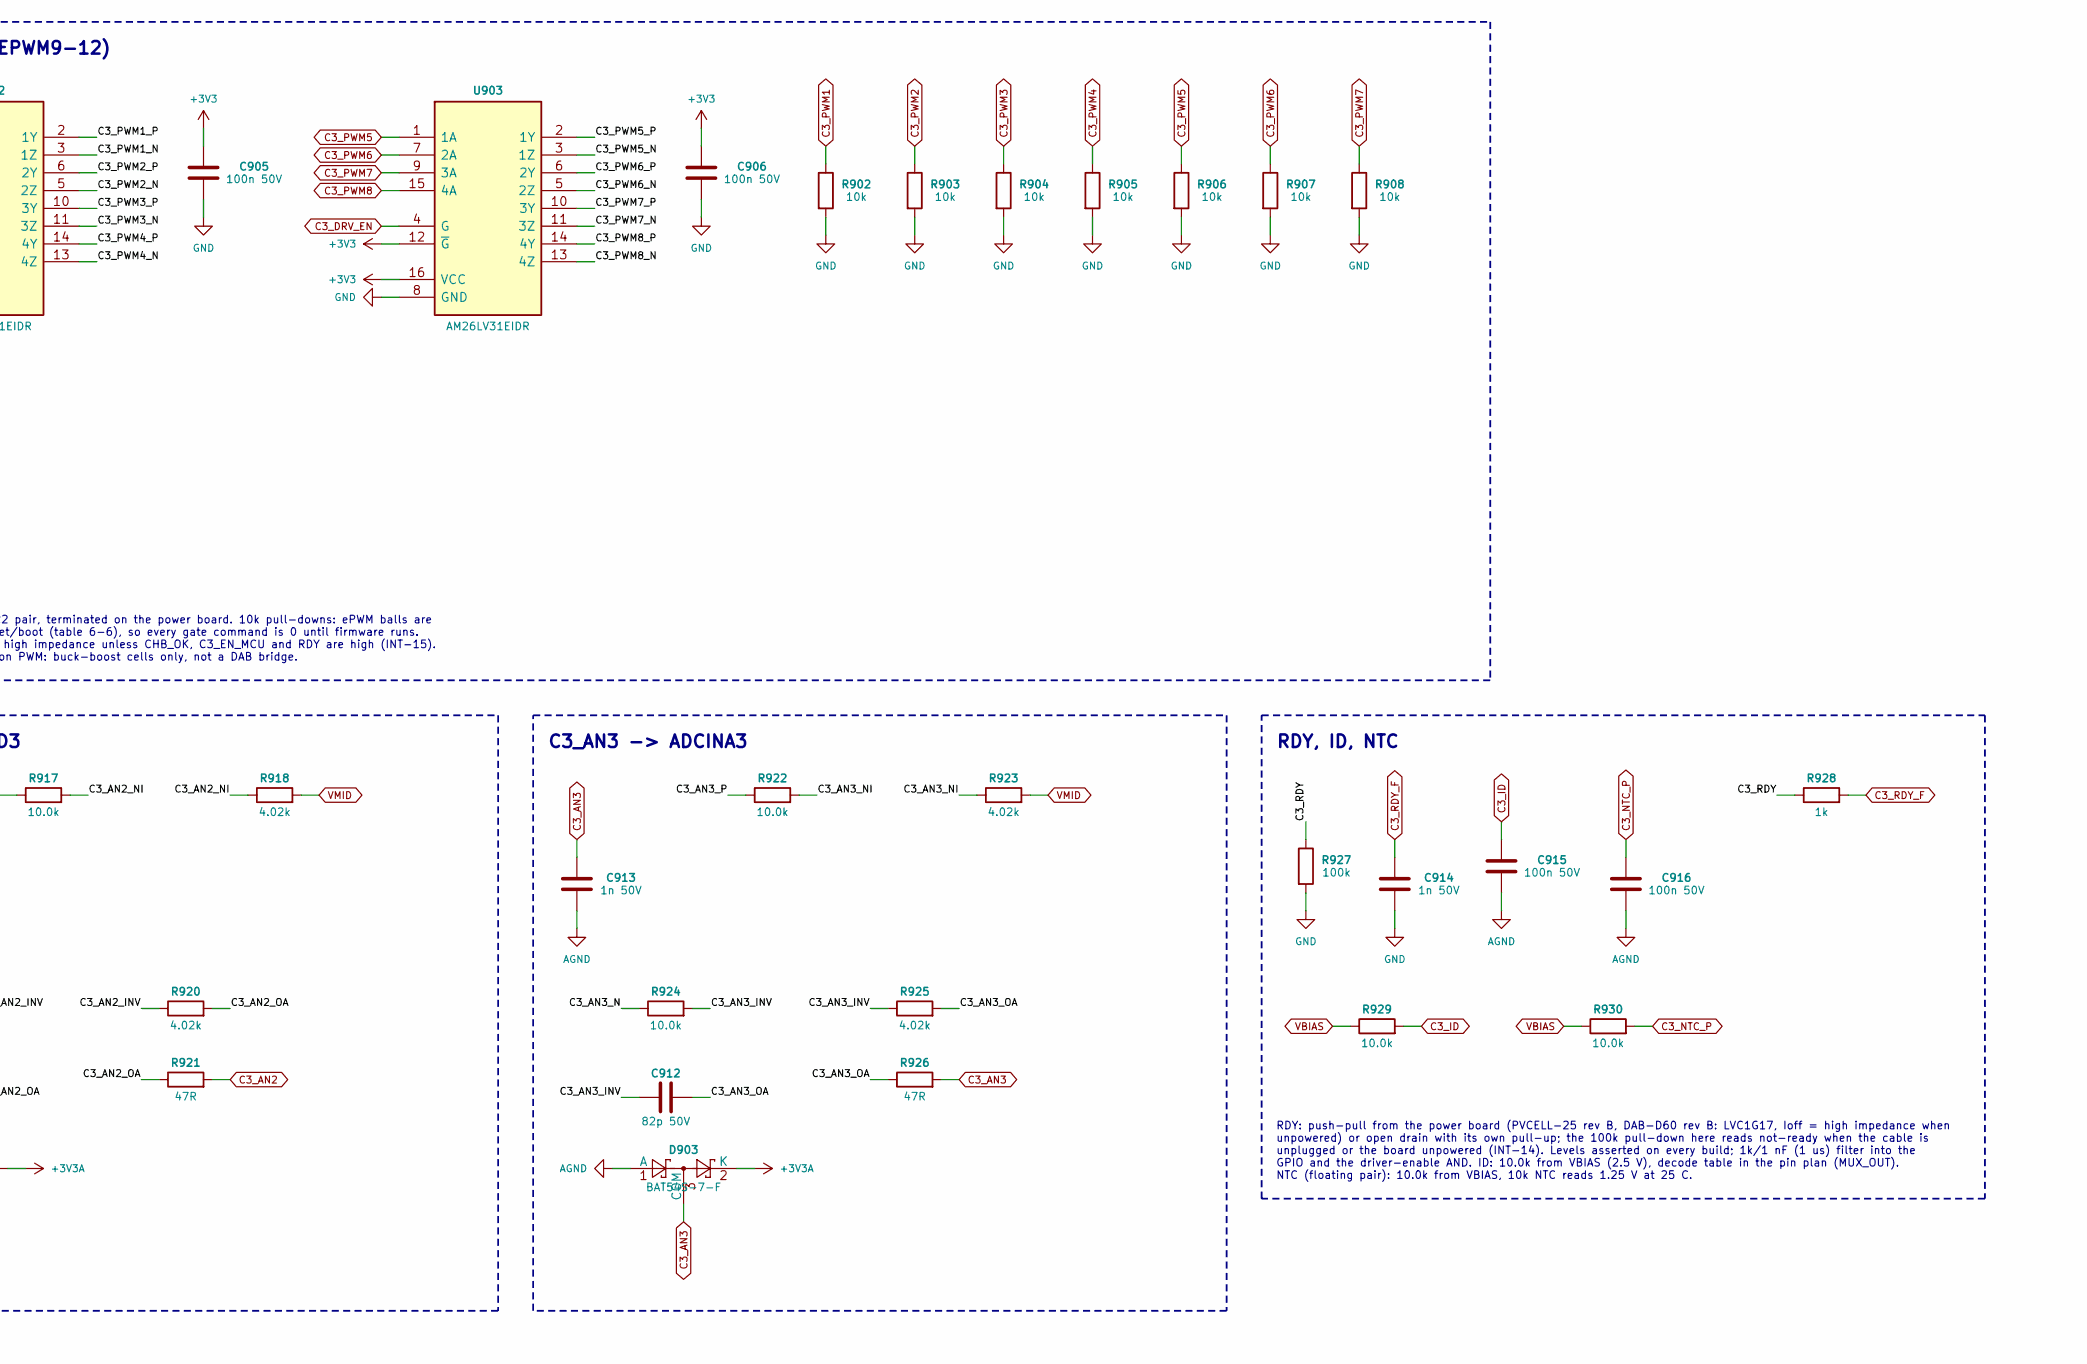
[picture p200: schematic 09_cell3.kicad_sch, part in row 1, column 2]

Parts:
C901: 10u 50V
C902: 100n 100V
C903: 1u 50V
C904: 680n 50V
C905, C906, C907, C915, C916: 100n 50V
C908, C910, C912: 82p 50V
C909, C911, C913, C914: 1n 50V
D901, D902, D903: BAT54S-7-F; MPN BAT54S-7-F
J901: 61204021621; MPN 61204021621
R901: 8.06k
R902, R903, R904, R905, R906, R907, R908, R909: 10k
R910, R912, R917, R919, R922, R924, R929, R930: 10.0k
R911, R913, R918, R920, R923, R925: 4.02k
R914, R921, R926: 47R
R915, R916: 1.50k
R927: 100k
R928: 1k
U901: TPS26600PWPR; MPN TPS26600PWPR
U902, U903: AM26LV31EIDR; MPN AM26LV31EIDR
U904: OPA4388IPWR; MPN OPA4388IPWR

Connections:
+3V3: C905.1, C906.1, U902.12 (~G), U902.16 (VCC), U903.12 (~G), U903.16 (VCC)
+3V3A: C907.1, D901.2 (K), D902.2 (K), D903.2 (K), R916.2, U904.4 (V+)
+24V_GD: C903.1, U901.1 (IN), U901.2 (IN)
AGND: C907.2, C909.2, C911.2, C913.2, C915.2, C916.2, D901.1 (A), D902.1 (A), D903.1 (A), J901.37, J901.38, J901.40, R915.2, U904.11 (V-)
C3_24V: C901.1, C902.1, J901.1, J901.2, U901.15 (OUT), U901.16 (OUT)
C3_AN1: C909.1, D901.3 (COM), R914.2
C3_AN1_INV: C908.1, R912.2, R913.1, U904.2 (-INA)
C3_AN1_N: J901.32, R912.1, R916.1
C3_AN1_NI: R910.2, R911.1, U904.3 (+INA)
C3_AN1_OA: C908.2, R913.2, R914.1, U904.1 (OUTA)
C3_AN1_P: J901.31, R910.1, R915.1
C3_AN2: C911.1, D902.3 (COM), R921.2
C3_AN2_INV: C910.1, R919.2, R920.1, U904.6 (-INB)
C3_AN2_N: J901.34, R919.1
C3_AN2_NI: R917.2, R918.1, U904.5 (+INB)
C3_AN2_OA: C910.2, R920.2, R921.1, U904.7 (OUTB)
C3_AN2_P: J901.33, R917.1
C3_AN3: C913.1, D903.3 (COM), R926.2
C3_AN3_INV: C912.1, R924.2, R925.1, U904.9 (-INC)
C3_AN3_N: J901.36, R924.1
C3_AN3_NI: R922.2, R923.1, U904.10 (+INC)
C3_AN3_OA: C912.2, R925.2, R926.1, U904.8 (OUTC)
C3_AN3_P: J901.35, R922.1
C3_DRV_EN: U902.4 (G), U903.4 (G)
C3_DVDT: C904.1, U901.12 (dVdT)
C3_EN_N: J901.28
C3_EN_P: J901.27
C3_FLT_N: J901.26
C3_FLT_P: J901.25
C3_ID: C915.1, J901.30, R929.2
C3_ILIM: R901.1, U901.11 (ILIM)
C3_NTC_P: C916.1, J901.39, R930.2
C3_PWM1: R902.1, U902.1 (1A)
C3_PWM1_N: J901.6, U902.3 (1Z)
C3_PWM1_P: J901.5, U902.2 (1Y)
C3_PWM2: R903.1, U902.7 (2A)
C3_PWM2_N: J901.8, U902.5 (2Z)
C3_PWM2_P: J901.7, U902.6 (2Y)
C3_PWM3: R904.1, U902.9 (3A)
C3_PWM3_N: J901.10, U902.11 (3Z)
C3_PWM3_P: J901.9, U902.10 (3Y)
C3_PWM4: R905.1, U902.15 (4A)
C3_PWM4_N: J901.12, U902.13 (4Z)
C3_PWM4_P: J901.11, U902.14 (4Y)
C3_PWM5: R906.1, U903.1 (1A)
C3_PWM5_N: J901.16, U903.3 (1Z)
C3_PWM5_P: J901.15, U903.2 (1Y)
C3_PWM6: R907.1, U903.7 (2A)
C3_PWM6_N: J901.18, U903.5 (2Z)
C3_PWM6_P: J901.17, U903.6 (2Y)
C3_PWM7: R908.1, U903.9 (3A)
C3_PWM7_N: J901.20, U903.11 (3Z)
C3_PWM7_P: J901.19, U903.10 (3Y)
C3_PWM8: R909.1, U903.15 (4A)
C3_PWM8_N: J901.22, U903.13 (4Z)
C3_PWM8_P: J901.21, U903.14 (4Y)
C3_RDY: J901.29, R927.1, R928.1
C3_RDY_F: C914.1, R928.2
C3_SPARE_D: U904.13 (-IND), U904.14 (OUTD)
GND: C901.2, C902.2, C903.2, C904.2, C905.2, C906.2, C914.2, J901.3, J901.4, J901.13, J901.14, J901.23, J901.24, R901.2, R902.2, R903.2, R904.2, R905.2, R906.2, R907.2, R908.2, R909.2, R927.2, U901.3 (UVLO), U901.5 (OVP), U901.8 (RTN), U901.9 (GND), U901.17 (PAD), U902.8 (GND), U903.8 (GND)
VBIAS: R929.1, R930.1
VMID: R911.2, R918.2, R923.2, U904.12 (+IND)

Notes on the sheet:
TPS26600, MODE open: circuit breaker I(CB) 1.30-1.61 A (RILIM 8.06k 1 %, eq. 4 + table 7.5), 4 ms, 540 ms auto-retry; factory UVLO 15 V / OVP 32.6 V (UVLO, OVP to RTN); SHDN open = on (self-biased 2.7 V). dVdT 680n (CSR-03): 0.13-0.23 V/ms, 26.4 V in 115-208 ms; 600 uF draws <= 0.137 A, so start-up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
Pin map = interfaces.CELL. Pins 1-2 carry +24V_GD only (gate-driver bias, channel B switched). NTC_N returns to AGND here; FLT/EN pairs go to the trip sheet.
RDY, ID, NTC
RDY: push-pull from the power board (PVCELL-25 rev B, DAB-D60 rev B: LVC1G17, Ioff = high impedance when unpowered) or open drain with its own pull-up; the 100k pull-down here reads not-ready when the cable is unplugged or the board unpowered (INT-14). Levels asserted on every build; 1k/1 nF (1 us)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
PWMk (1 = switch on) -> RS-422 pair, terminated on the power board. 10k pull-downs: ePWM balls are inputs without pull-up during reset/boot (table 6-6), so every gate command is 0 until firmware runs. G = C3_DRV_EN, G~ high: outputs high impedance unless CHB_OK, C3_EN_MCU and RDY are high (INT-15).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
ANALOG FRONT ENDS AN1-AN3 (OPA4388), DUAL RANGE
+24V_GD EFUSE FOR C3 (<= 1.0 A CONTINUOUS, <= 600 UF)
Difference amp per pair: Vadc = VMID 1.25 V + G x (AN_P - AN_N), Rin 10.0k 0.1 % 10 ppm/K. G = 4.02k/10.0k = 0.402. Cf || Rf: anti-alias pole 483 kHz. 47 R + 1 nF C0G: ADC charge bucket (ACQPS >= 320 ns at 12 bit). BAT54S clamps the ADC node to 3V3A/AGND. All values calculated, not simulated. Accep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
C3_AN1 -> ADCINC2 / CMPIN6P
C3_AN3 -> ADCINA3
C3_AN2 -> ADCIND3
PWM LINE DRIVERS (EPWM9-12)
C3 CONNECTOR (CELL CONTRACT)
