vectivolt/PCM/hardware/CTRL-C2000/sheets/10_cell4.kicad_sch

## KiCad design hardware/CTRL-C2000/sheets/10_cell4.kicad_sch (2026-10-04)

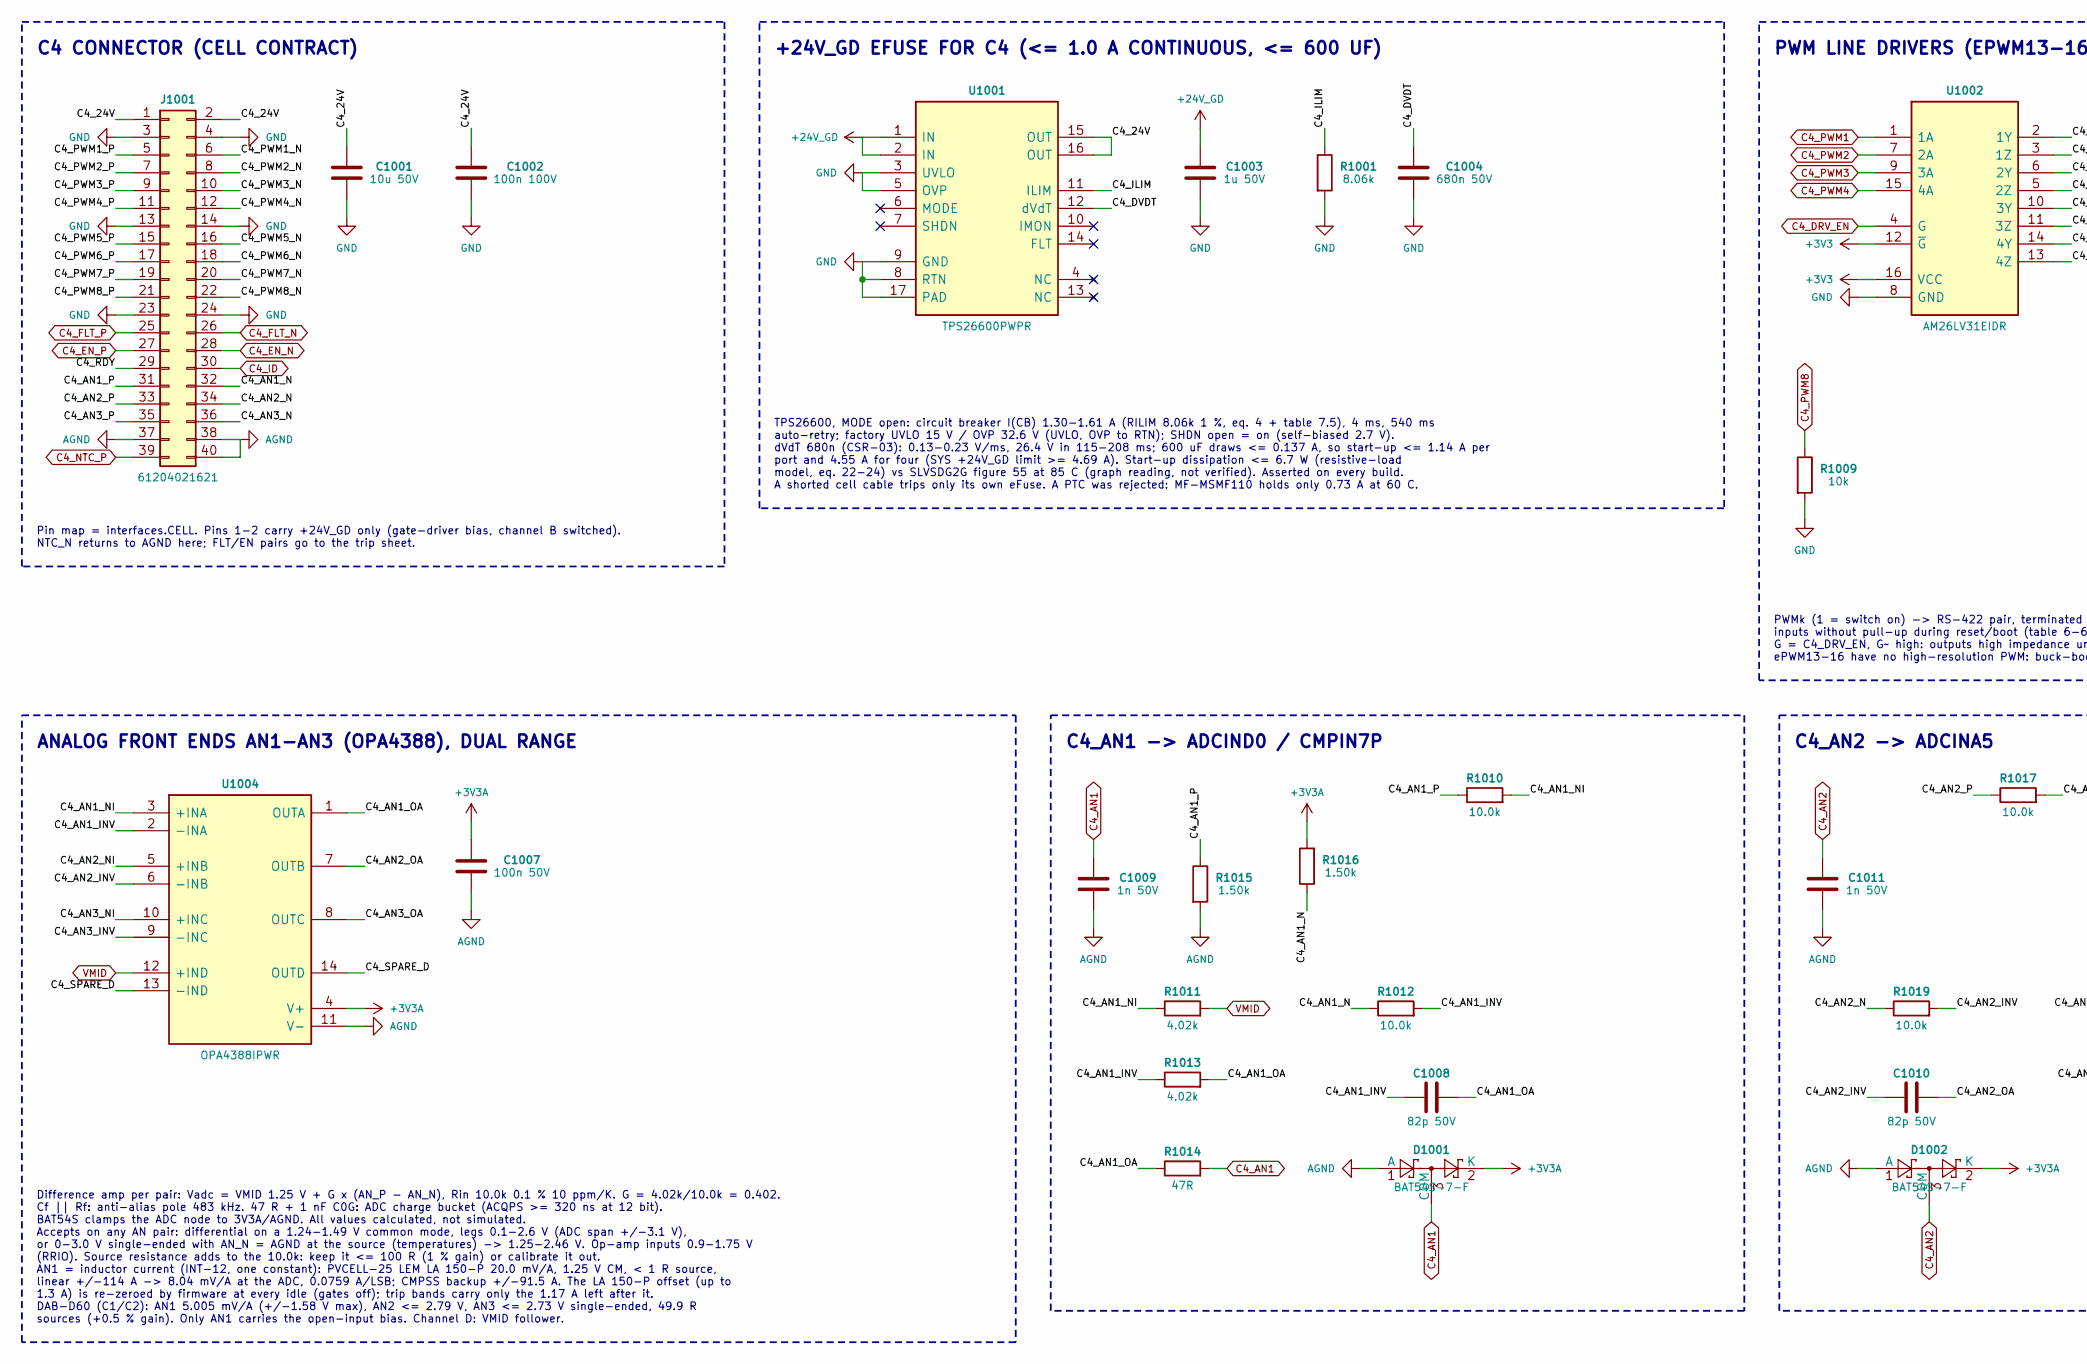
[picture p201: schematic 10_cell4.kicad_sch, part in row 1, column 1]

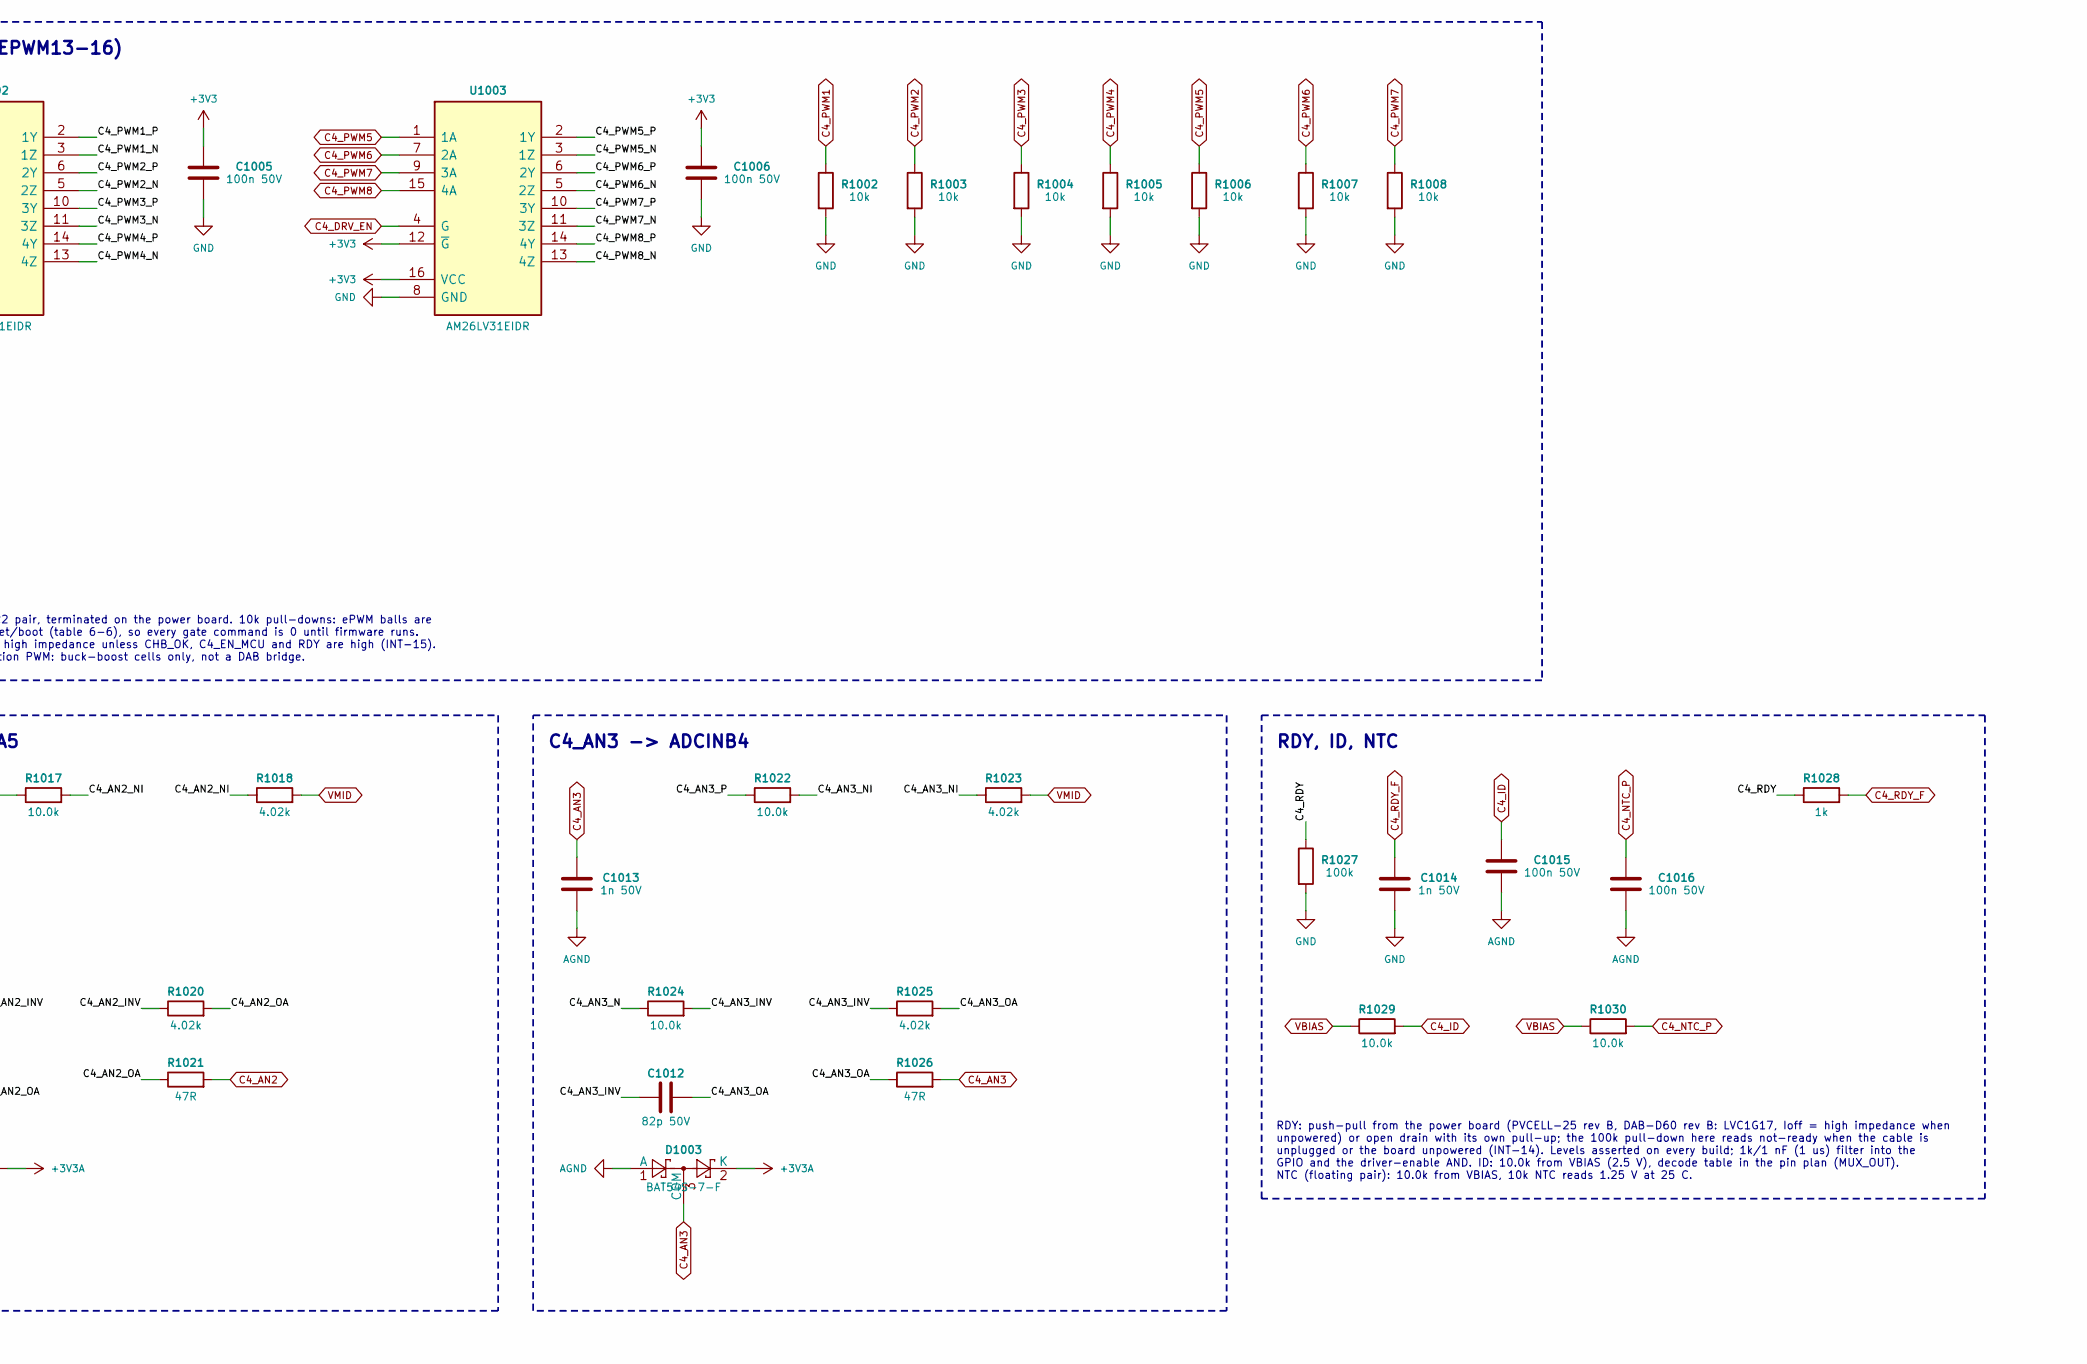
[picture p202: schematic 10_cell4.kicad_sch, part in row 1, column 2]

Parts:
C1001: 10u 50V
C1002: 100n 100V
C1003: 1u 50V
C1004: 680n 50V
C1005, C1006, C1007, C1015, C1016: 100n 50V
C1008, C1010, C1012: 82p 50V
C1009, C1011, C1013, C1014: 1n 50V
D1001, D1002, D1003: BAT54S-7-F; MPN BAT54S-7-F
J1001: 61204021621; MPN 61204021621
R1001: 8.06k
R1002, R1003, R1004, R1005, R1006, R1007, R1008, R1009: 10k
R1010, R1012, R1017, R1019, R1022, R1024, R1029, R1030: 10.0k
R1011, R1013, R1018, R1020, R1023, R1025: 4.02k
R1014, R1021, R1026: 47R
R1015, R1016: 1.50k
R1027: 100k
R1028: 1k
U1001: TPS26600PWPR; MPN TPS26600PWPR
U1002, U1003: AM26LV31EIDR; MPN AM26LV31EIDR
U1004: OPA4388IPWR; MPN OPA4388IPWR

Connections:
+3V3: C1005.1, C1006.1, U1002.12 (~G), U1002.16 (VCC), U1003.12 (~G), U1003.16 (VCC)
+3V3A: C1007.1, D1001.2 (K), D1002.2 (K), D1003.2 (K), R1016.2, U1004.4 (V+)
+24V_GD: C1003.1, U1001.1 (IN), U1001.2 (IN)
AGND: C1007.2, C1009.2, C1011.2, C1013.2, C1015.2, C1016.2, D1001.1 (A), D1002.1 (A), D1003.1 (A), J1001.37, J1001.38, J1001.40, R1015.2, U1004.11 (V-)
C4_24V: C1001.1, C1002.1, J1001.1, J1001.2, U1001.15 (OUT), U1001.16 (OUT)
C4_AN1: C1009.1, D1001.3 (COM), R1014.2
C4_AN1_INV: C1008.1, R1012.2, R1013.1, U1004.2 (-INA)
C4_AN1_N: J1001.32, R1012.1, R1016.1
C4_AN1_NI: R1010.2, R1011.1, U1004.3 (+INA)
C4_AN1_OA: C1008.2, R1013.2, R1014.1, U1004.1 (OUTA)
C4_AN1_P: J1001.31, R1010.1, R1015.1
C4_AN2: C1011.1, D1002.3 (COM), R1021.2
C4_AN2_INV: C1010.1, R1019.2, R1020.1, U1004.6 (-INB)
C4_AN2_N: J1001.34, R1019.1
C4_AN2_NI: R1017.2, R1018.1, U1004.5 (+INB)
C4_AN2_OA: C1010.2, R1020.2, R1021.1, U1004.7 (OUTB)
C4_AN2_P: J1001.33, R1017.1
C4_AN3: C1013.1, D1003.3 (COM), R1026.2
C4_AN3_INV: C1012.1, R1024.2, R1025.1, U1004.9 (-INC)
C4_AN3_N: J1001.36, R1024.1
C4_AN3_NI: R1022.2, R1023.1, U1004.10 (+INC)
C4_AN3_OA: C1012.2, R1025.2, R1026.1, U1004.8 (OUTC)
C4_AN3_P: J1001.35, R1022.1
C4_DRV_EN: U1002.4 (G), U1003.4 (G)
C4_DVDT: C1004.1, U1001.12 (dVdT)
C4_EN_N: J1001.28
C4_EN_P: J1001.27
C4_FLT_N: J1001.26
C4_FLT_P: J1001.25
C4_ID: C1015.1, J1001.30, R1029.2
C4_ILIM: R1001.1, U1001.11 (ILIM)
C4_NTC_P: C1016.1, J1001.39, R1030.2
C4_PWM1: R1002.1, U1002.1 (1A)
C4_PWM1_N: J1001.6, U1002.3 (1Z)
C4_PWM1_P: J1001.5, U1002.2 (1Y)
C4_PWM2: R1003.1, U1002.7 (2A)
C4_PWM2_N: J1001.8, U1002.5 (2Z)
C4_PWM2_P: J1001.7, U1002.6 (2Y)
C4_PWM3: R1004.1, U1002.9 (3A)
C4_PWM3_N: J1001.10, U1002.11 (3Z)
C4_PWM3_P: J1001.9, U1002.10 (3Y)
C4_PWM4: R1005.1, U1002.15 (4A)
C4_PWM4_N: J1001.12, U1002.13 (4Z)
C4_PWM4_P: J1001.11, U1002.14 (4Y)
C4_PWM5: R1006.1, U1003.1 (1A)
C4_PWM5_N: J1001.16, U1003.3 (1Z)
C4_PWM5_P: J1001.15, U1003.2 (1Y)
C4_PWM6: R1007.1, U1003.7 (2A)
C4_PWM6_N: J1001.18, U1003.5 (2Z)
C4_PWM6_P: J1001.17, U1003.6 (2Y)
C4_PWM7: R1008.1, U1003.9 (3A)
C4_PWM7_N: J1001.20, U1003.11 (3Z)
C4_PWM7_P: J1001.19, U1003.10 (3Y)
C4_PWM8: R1009.1, U1003.15 (4A)
C4_PWM8_N: J1001.22, U1003.13 (4Z)
C4_PWM8_P: J1001.21, U1003.14 (4Y)
C4_RDY: J1001.29, R1027.1, R1028.1
C4_RDY_F: C1014.1, R1028.2
C4_SPARE_D: U1004.13 (-IND), U1004.14 (OUTD)
GND: C1001.2, C1002.2, C1003.2, C1004.2, C1005.2, C1006.2, C1014.2, J1001.3, J1001.4, J1001.13, J1001.14, J1001.23, J1001.24, R1001.2, R1002.2, R1003.2, R1004.2, R1005.2, R1006.2, R1007.2, R1008.2, R1009.2, R1027.2, U1001.3 (UVLO), U1001.5 (OVP), U1001.8 (RTN), U1001.9 (GND), U1001.17 (PAD), U1002.8 (GND), U1003.8 (GND)
VBIAS: R1029.1, R1030.1
VMID: R1011.2, R1018.2, R1023.2, U1004.12 (+IND)

Notes on the sheet:
C4_AN3 -> ADCINB4
PWM LINE DRIVERS (EPWM13-16)
Difference amp per pair: Vadc = VMID 1.25 V + G x (AN_P - AN_N), Rin 10.0k 0.1 % 10 ppm/K. G = 4.02k/10.0k = 0.402. Cf || Rf: anti-alias pole 483 kHz. 47 R + 1 nF C0G: ADC charge bucket (ACQPS >= 320 ns at 12 bit). BAT54S clamps the ADC node to 3V3A/AGND. All values calculated, not simulated. Accep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
C4_AN2 -> ADCINA5
RDY: push-pull from the power board (PVCELL-25 rev B, DAB-D60 rev B: LVC1G17, Ioff = high impedance when unpowered) or open drain with its own pull-up; the 100k pull-down here reads not-ready when the cable is unplugged or the board unpowered (INT-14). Levels asserted on every build; 1k/1 nF (1 us)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
Pin map = interfaces.CELL. Pins 1-2 carry +24V_GD only (gate-driver bias, channel B switched). NTC_N returns to AGND here; FLT/EN pairs go to the trip sheet.
RDY, ID, NTC
C4 CONNECTOR (CELL CONTRACT)
PWMk (1 = switch on) -> RS-422 pair, terminated on the power board. 10k pull-downs: ePWM balls are inputs without pull-up during reset/boot (table 6-6), so every gate command is 0 until firmware runs. G = C4_DRV_EN, G~ high: outputs high impedance unless CHB_OK, C4_EN_MCU and RDY are high (INT-15).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
ANALOG FRONT ENDS AN1-AN3 (OPA4388), DUAL RANGE
TPS26600, MODE open: circuit breaker I(CB) 1.30-1.61 A (RILIM 8.06k 1 %, eq. 4 + table 7.5), 4 ms, 540 ms auto-retry; factory UVLO 15 V / OVP 32.6 V (UVLO, OVP to RTN); SHDN open = on (self-biased 2.7 V). dVdT 680n (CSR-03): 0.13-0.23 V/ms, 26.4 V in 115-208 ms; 600 uF draws <= 0.137 A, so start-up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
+24V_GD EFUSE FOR C4 (<= 1.0 A CONTINUOUS, <= 600 UF)
C4_AN1 -> ADCIND0 / CMPIN7P
