vectivolt/PCM/hardware/CTRL-C2000/sheets/11_port.kicad_sch

## KiCad design hardware/CTRL-C2000/sheets/11_port.kicad_sch (2026-10-04)

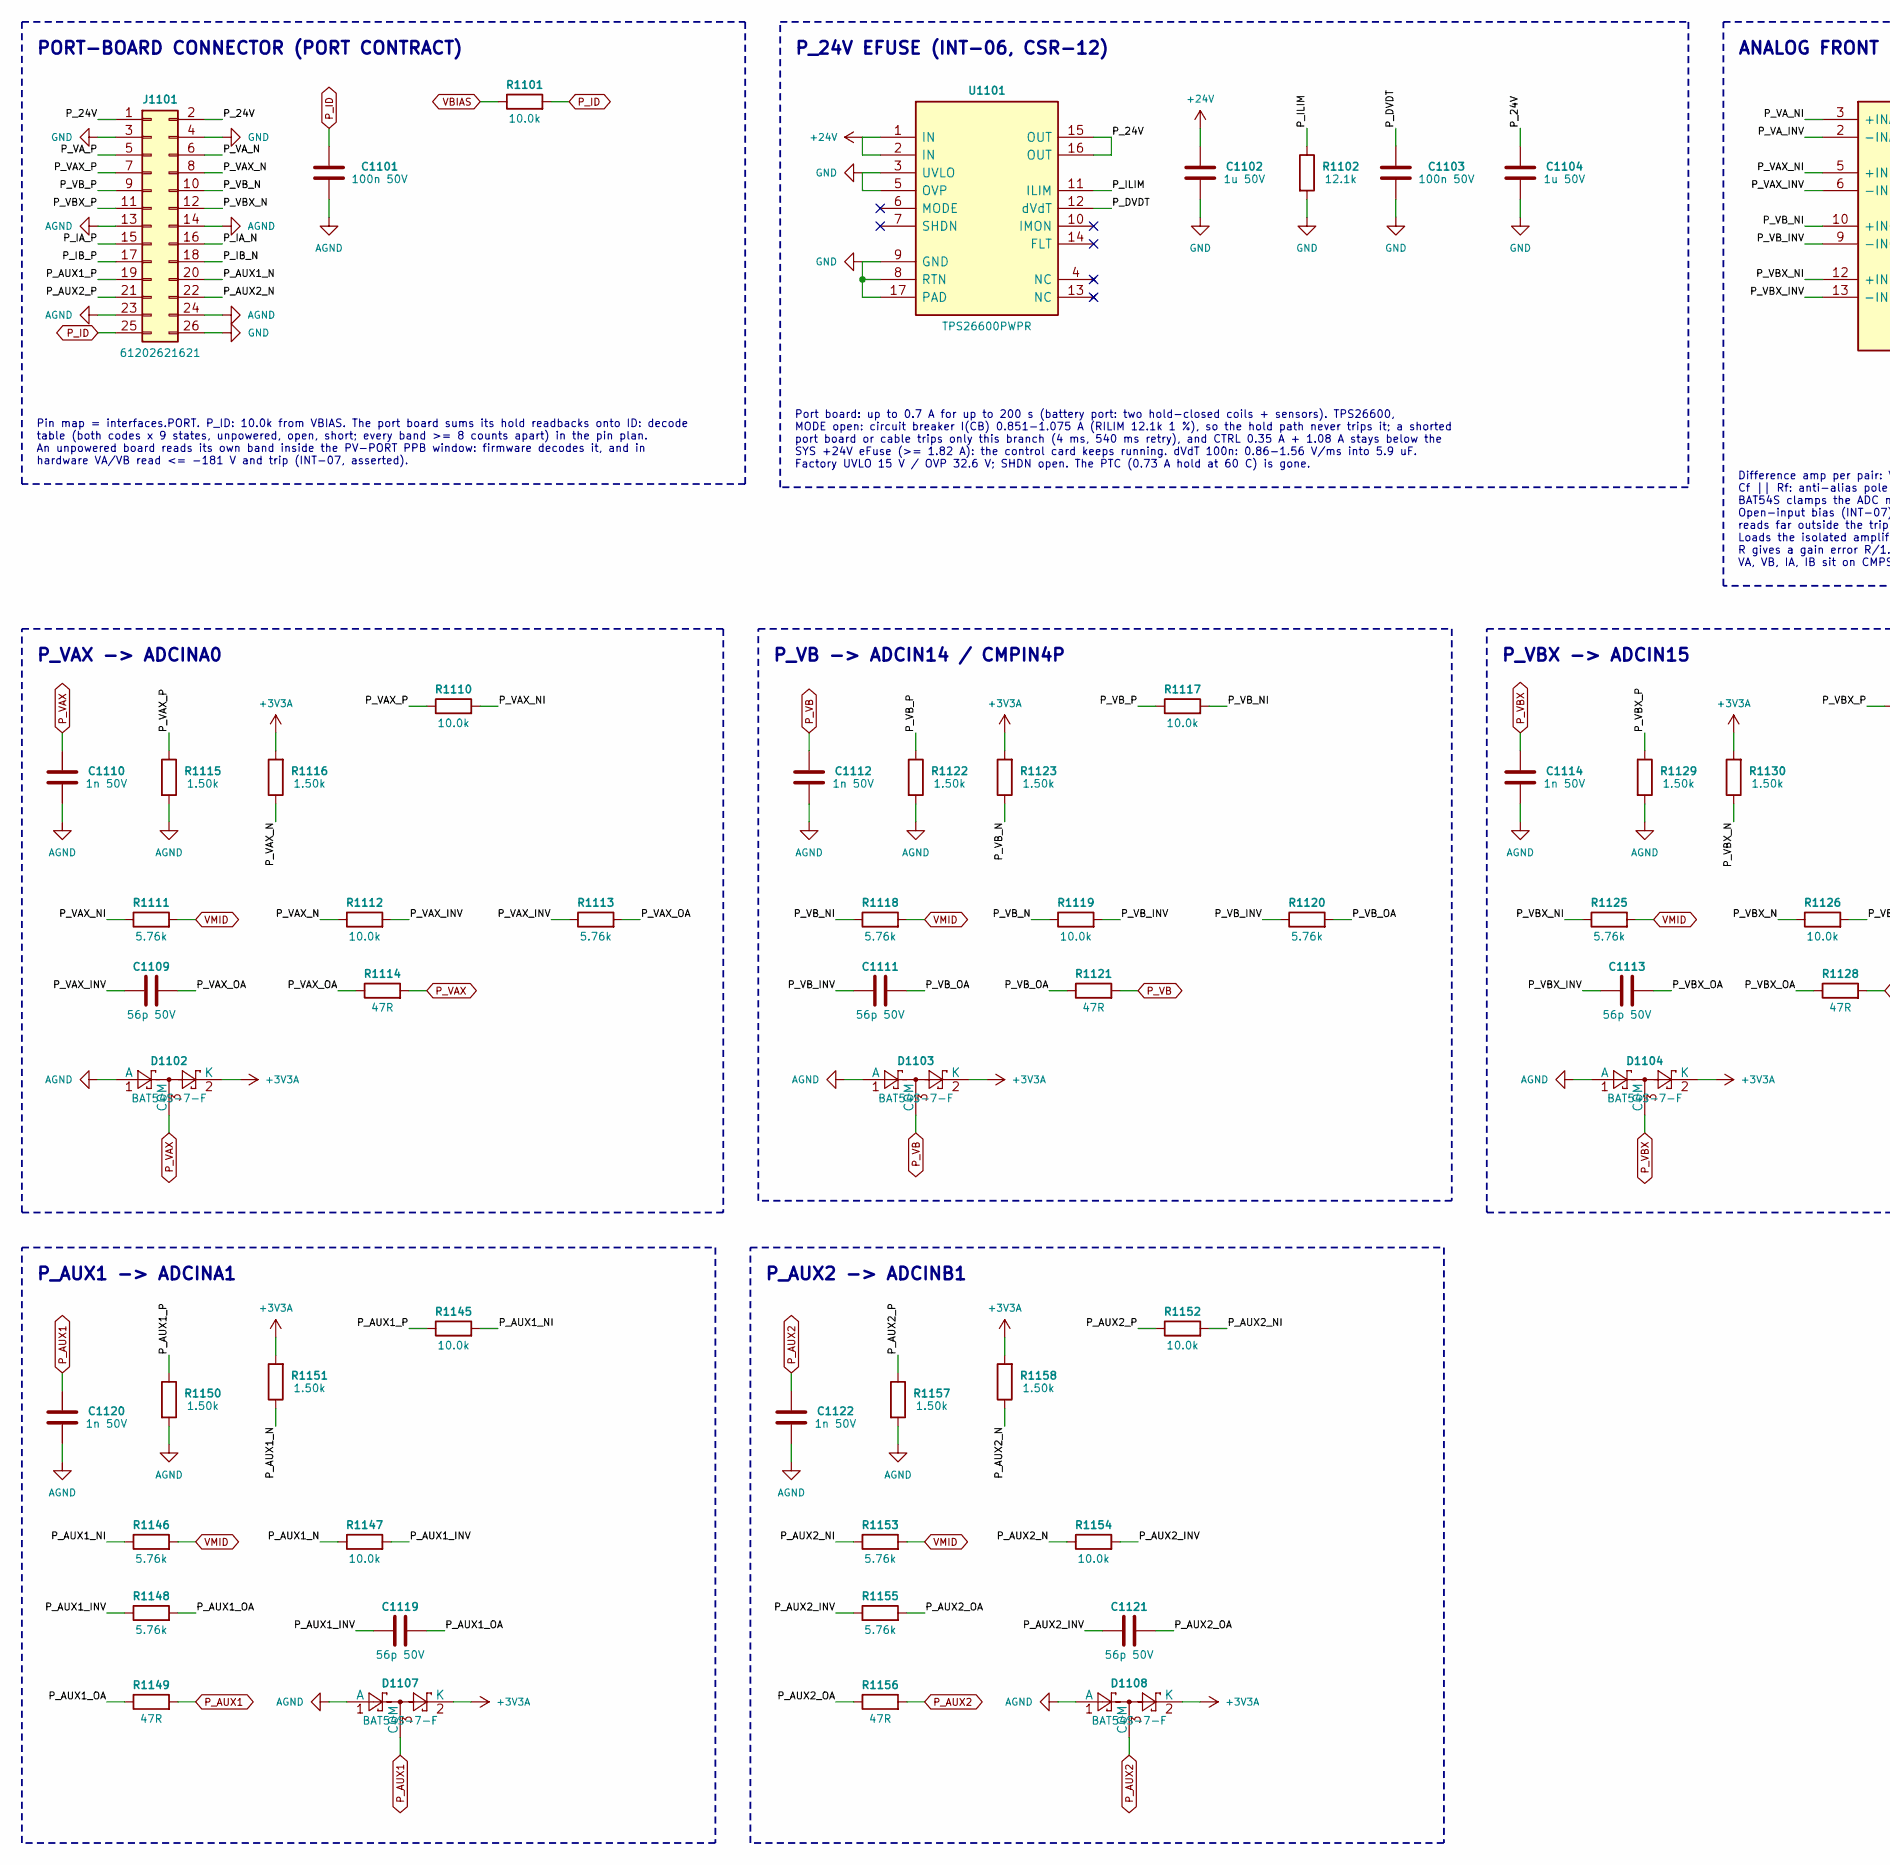
[picture p203: schematic 11_port.kicad_sch, part in row 1, column 1]

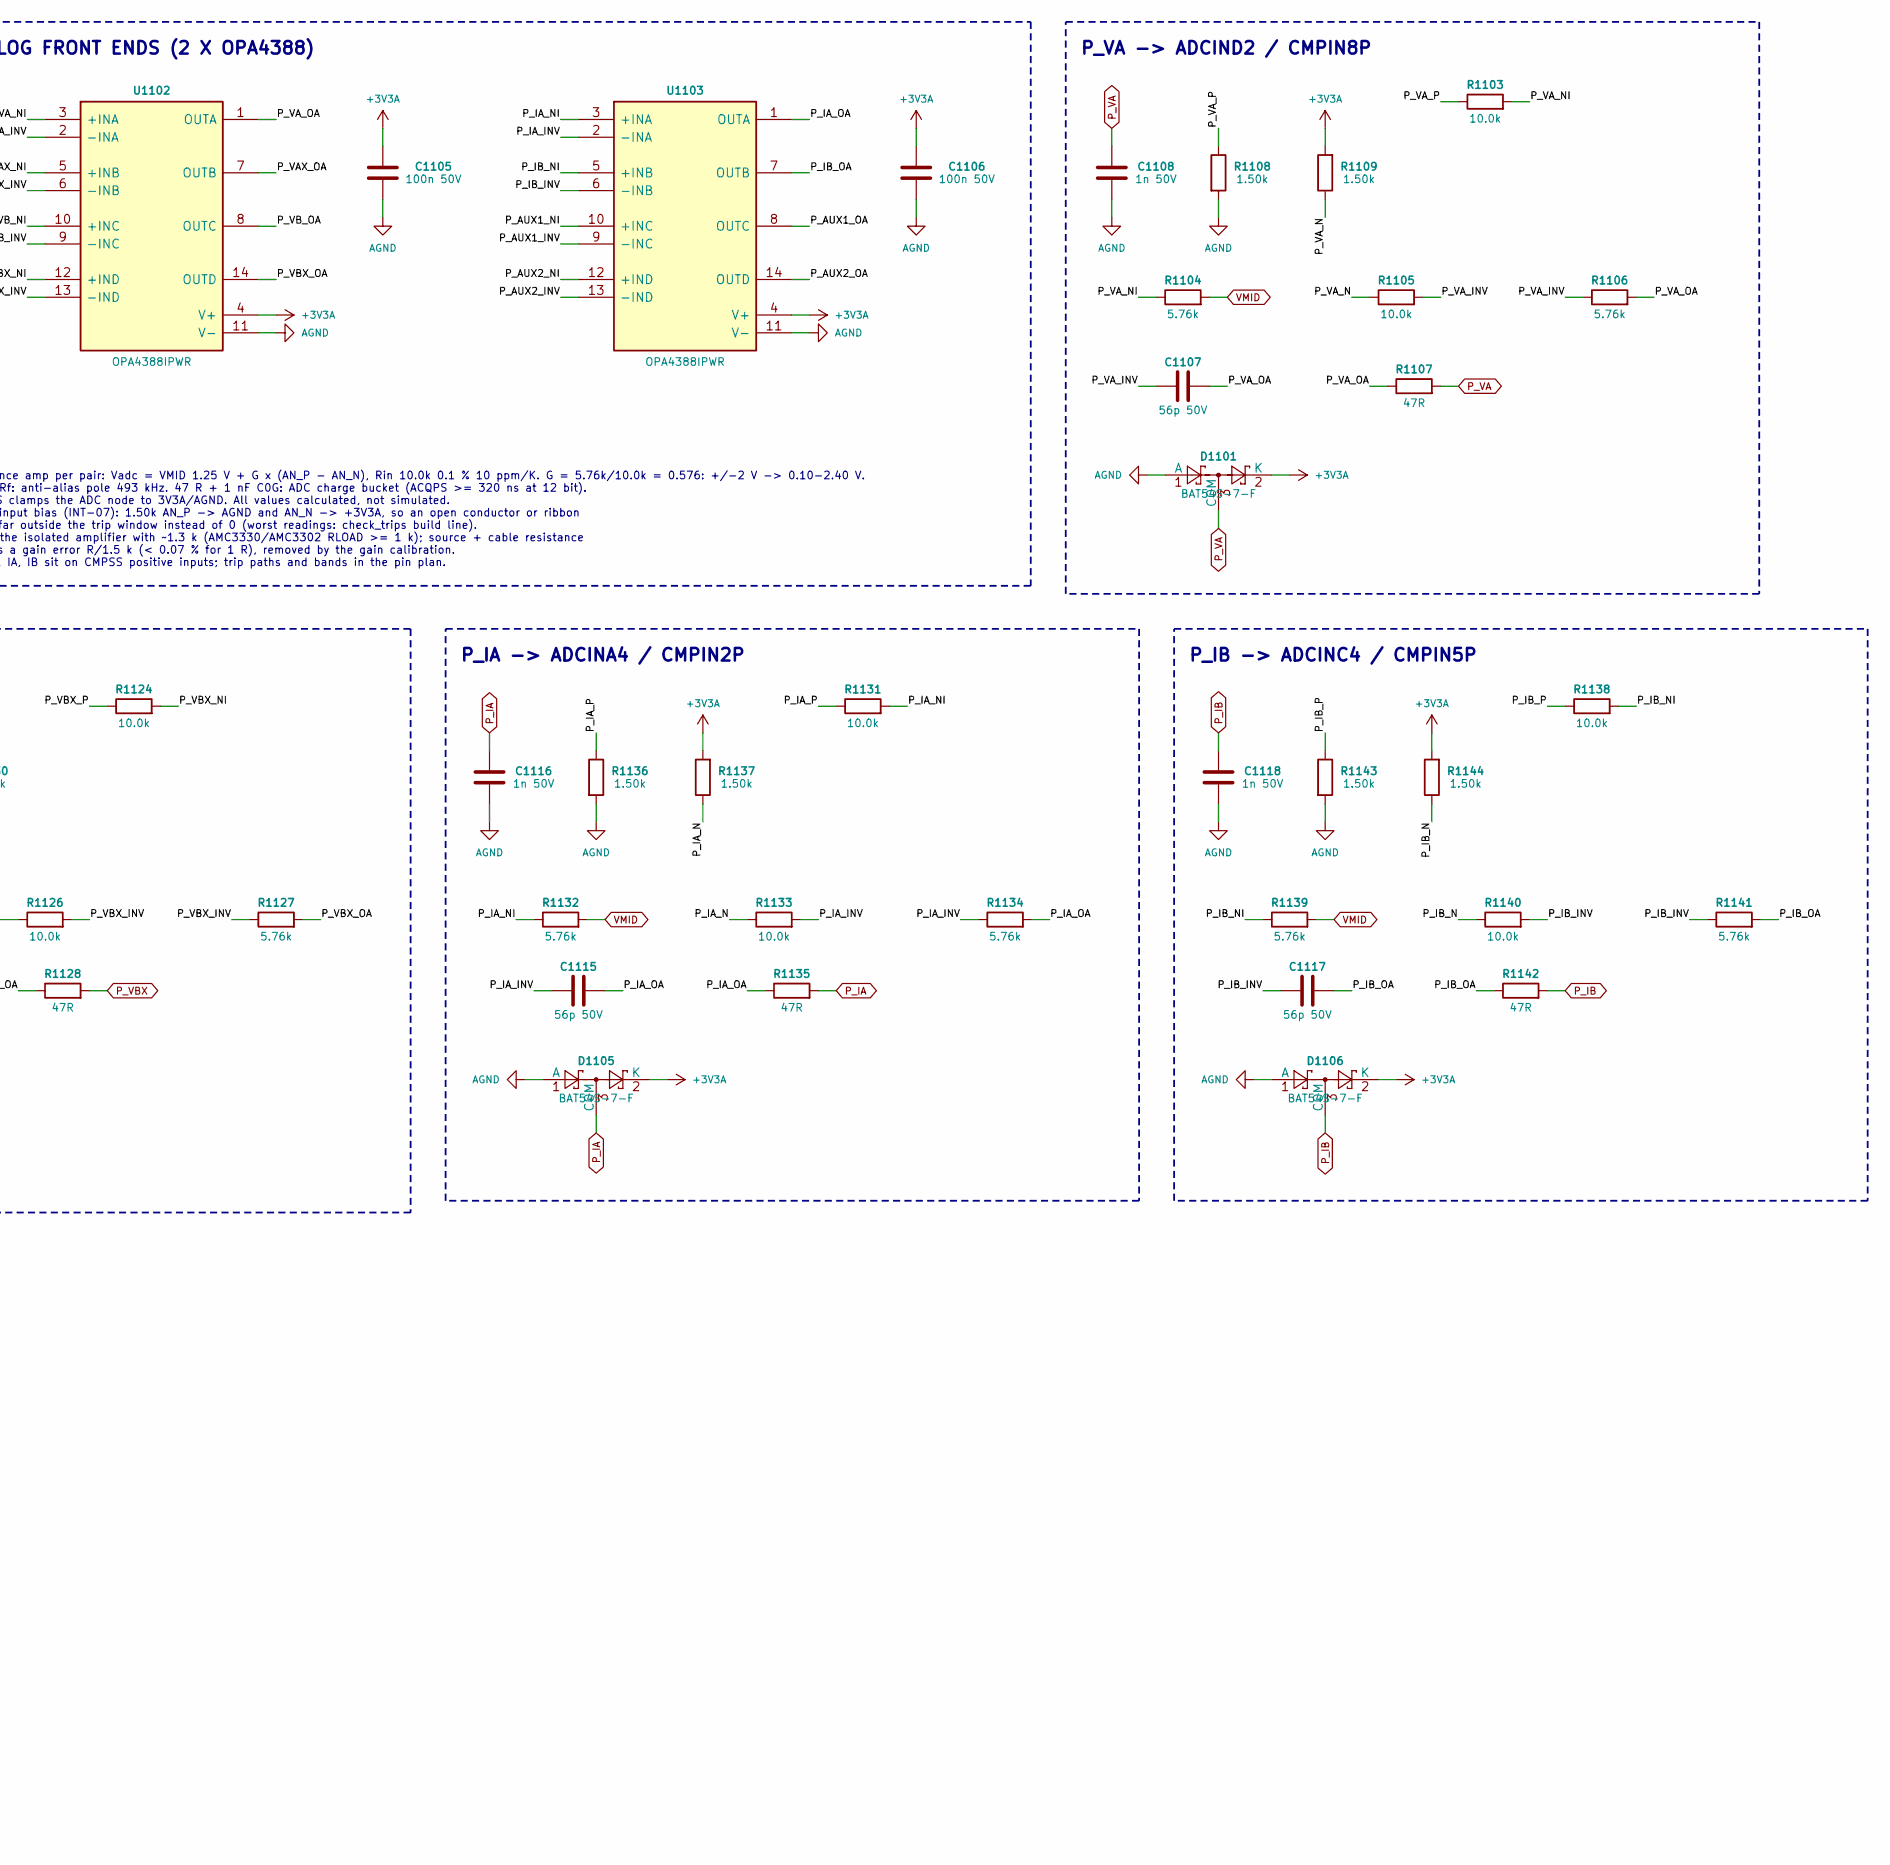
[picture p204: schematic 11_port.kicad_sch, part in row 1, column 2]

Parts:
C1101, C1103, C1105, C1106: 100n 50V
C1102, C1104: 1u 50V
C1107, C1109, C1111, C1113, C1115, C1117, C1119, C1121: 56p 50V
C1108, C1110, C1112, C1114, C1116, C1118, C1120, C1122: 1n 50V
D1101, D1102, D1103, D1104, D1105, D1106, D1107, D1108: BAT54S-7-F; MPN BAT54S-7-F
J1101: 61202621621; MPN 61202621621
R1101, R1103, R1105, R1110, R1112, R1117, R1119, R1124, R1126, R1131, R1133, R1138, R1140, R1145, R1147, R1152, R1154: 10.0k
R1102: 12.1k
R1104, R1106, R1111, R1113, R1118, R1120, R1125, R1127, R1132, R1134, R1139, R1141, R1146, R1148, R1153, R1155: 5.76k
R1107, R1114, R1121, R1128, R1135, R1142, R1149, R1156: 47R
R1108, R1109, R1115, R1116, R1122, R1123, R1129, R1130, R1136, R1137, R1143, R1144, R1150, R1151, R1157, R1158: 1.50k
U1101: TPS26600PWPR; MPN TPS26600PWPR
U1102, U1103: OPA4388IPWR; MPN OPA4388IPWR

Connections:
+3V3A: C1105.1, C1106.1, D1101.2 (K), D1102.2 (K), D1103.2 (K), D1104.2 (K), D1105.2 (K), D1106.2 (K), D1107.2 (K), D1108.2 (K), R1109.2, R1116.2, R1123.2, R1130.2, R1137.2, R1144.2, R1151.2, R1158.2, U1102.4 (V+), U1103.4 (V+)
+24V: C1102.1, U1101.1 (IN), U1101.2 (IN)
AGND: C1101.2, C1105.2, C1106.2, C1108.2, C1110.2, C1112.2, C1114.2, C1116.2, C1118.2, C1120.2, C1122.2, D1101.1 (A), D1102.1 (A), D1103.1 (A), D1104.1 (A), D1105.1 (A), D1106.1 (A), D1107.1 (A), D1108.1 (A), J1101.13, J1101.14, J1101.23, J1101.24, R1108.2, R1115.2, R1122.2, R1129.2, R1136.2, R1143.2, R1150.2, R1157.2, U1102.11 (V-), U1103.11 (V-)
GND: C1102.2, C1103.2, C1104.2, J1101.3, J1101.4, J1101.26, R1102.2, U1101.3 (UVLO), U1101.5 (OVP), U1101.8 (RTN), U1101.9 (GND), U1101.17 (PAD)
P_24V: C1104.1, J1101.1, J1101.2, U1101.15 (OUT), U1101.16 (OUT)
P_AUX1: C1120.1, D1107.3 (COM), R1149.2
P_AUX1_INV: C1119.1, R1147.2, R1148.1, U1103.9 (-INC)
P_AUX1_N: J1101.20, R1147.1, R1151.1
P_AUX1_NI: R1145.2, R1146.1, U1103.10 (+INC)
P_AUX1_OA: C1119.2, R1148.2, R1149.1, U1103.8 (OUTC)
P_AUX1_P: J1101.19, R1145.1, R1150.1
P_AUX2: C1122.1, D1108.3 (COM), R1156.2
P_AUX2_INV: C1121.1, R1154.2, R1155.1, U1103.13 (-IND)
P_AUX2_N: J1101.22, R1154.1, R1158.1
P_AUX2_NI: R1152.2, R1153.1, U1103.12 (+IND)
P_AUX2_OA: C1121.2, R1155.2, R1156.1, U1103.14 (OUTD)
P_AUX2_P: J1101.21, R1152.1, R1157.1
P_DVDT: C1103.1, U1101.12 (dVdT)
P_IA: C1116.1, D1105.3 (COM), R1135.2
P_IA_INV: C1115.1, R1133.2, R1134.1, U1103.2 (-INA)
P_IA_N: J1101.16, R1133.1, R1137.1
P_IA_NI: R1131.2, R1132.1, U1103.3 (+INA)
P_IA_OA: C1115.2, R1134.2, R1135.1, U1103.1 (OUTA)
P_IA_P: J1101.15, R1131.1, R1136.1
P_IB: C1118.1, D1106.3 (COM), R1142.2
P_IB_INV: C1117.1, R1140.2, R1141.1, U1103.6 (-INB)
P_IB_N: J1101.18, R1140.1, R1144.1
P_IB_NI: R1138.2, R1139.1, U1103.5 (+INB)
P_IB_OA: C1117.2, R1141.2, R1142.1, U1103.7 (OUTB)
P_IB_P: J1101.17, R1138.1, R1143.1
P_ID: C1101.1, J1101.25, R1101.2
P_ILIM: R1102.1, U1101.11 (ILIM)
P_VA: C1108.1, D1101.3 (COM), R1107.2
P_VAX: C1110.1, D1102.3 (COM), R1114.2
P_VAX_INV: C1109.1, R1112.2, R1113.1, U1102.6 (-INB)
P_VAX_N: J1101.8, R1112.1, R1116.1
P_VAX_NI: R1110.2, R1111.1, U1102.5 (+INB)
P_VAX_OA: C1109.2, R1113.2, R1114.1, U1102.7 (OUTB)
P_VAX_P: J1101.7, R1110.1, R1115.1
P_VA_INV: C1107.1, R1105.2, R1106.1, U1102.2 (-INA)
P_VA_N: J1101.6, R1105.1, R1109.1
P_VA_NI: R1103.2, R1104.1, U1102.3 (+INA)
P_VA_OA: C1107.2, R1106.2, R1107.1, U1102.1 (OUTA)
P_VA_P: J1101.5, R1103.1, R1108.1
P_VB: C1112.1, D1103.3 (COM), R1121.2
P_VBX: C1114.1, D1104.3 (COM), R1128.2
P_VBX_INV: C1113.1, R1126.2, R1127.1, U1102.13 (-IND)
P_VBX_N: J1101.12, R1126.1, R1130.1
P_VBX_NI: R1124.2, R1125.1, U1102.12 (+IND)
P_VBX_OA: C1113.2, R1127.2, R1128.1, U1102.14 (OUTD)
P_VBX_P: J1101.11, R1124.1, R1129.1
P_VB_INV: C1111.1, R1119.2, R1120.1, U1102.9 (-INC)
P_VB_N: J1101.10, R1119.1, R1123.1
P_VB_NI: R1117.2, R1118.1, U1102.10 (+INC)
P_VB_OA: C1111.2, R1120.2, R1121.1, U1102.8 (OUTC)
P_VB_P: J1101.9, R1117.1, R1122.1
VBIAS: R1101.1
VMID: R1104.2, R1111.2, R1118.2, R1125.2, R1132.2, R1139.2, R1146.2, R1153.2

Notes on the sheet:
ANALOG FRONT ENDS (2 X OPA4388)
P_VAX -> ADCINA0
Difference amp per pair: Vadc = VMID 1.25 V + G x (AN_P - AN_N), Rin 10.0k 0.1 % 10 ppm/K. G = 5.76k/10.0k = 0.576: +/-2 V -> 0.10-2.40 V. Cf || Rf: anti-alias pole 493 kHz. 47 R + 1 nF C0G: ADC charge bucket (ACQPS >= 320 ns at 12 bit). BAT54S clamps the ADC node to 3V3A/AGND. All values calculate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
P_24V EFUSE (INT-06, CSR-12)
P_IB -> ADCINC4 / CMPIN5P
Port board: up to 0.7 A for up to 200 s (battery port: two hold-closed coils + sensors). TPS26600, MODE open: circuit breaker I(CB) 0.851-1.075 A (RILIM 12.1k 1 %), so the hold path never trips it; a shorted port board or cable trips only this branch (4 ms, 540 ms retry), and CTRL 0.35 A + 1.08 A s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
Pin map = interfaces.PORT. P_ID: 10.0k from VBIAS. The port board sums its hold readbacks onto ID: decode table (both codes x 9 states, unpowered, open, short; every band >= 8 counts apart) in the pin plan. An unpowered board reads its own band inside the PV-PORT PPB window: firmware decodes it, an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
PORT-BOARD CONNECTOR (PORT CONTRACT)
P_VB -> ADCIN14 / CMPIN4P
P_AUX1 -> ADCINA1
P_AUX2 -> ADCINB1
P_VA -> ADCIND2 / CMPIN8P
P_VBX -> ADCIN15
P_IA -> ADCINA4 / CMPIN2P
