vectivolt/PCM/hardware/CTRL-C2000/sheets/12_sys.kicad_sch

## KiCad design hardware/CTRL-C2000/sheets/12_sys.kicad_sch (2026-10-04)

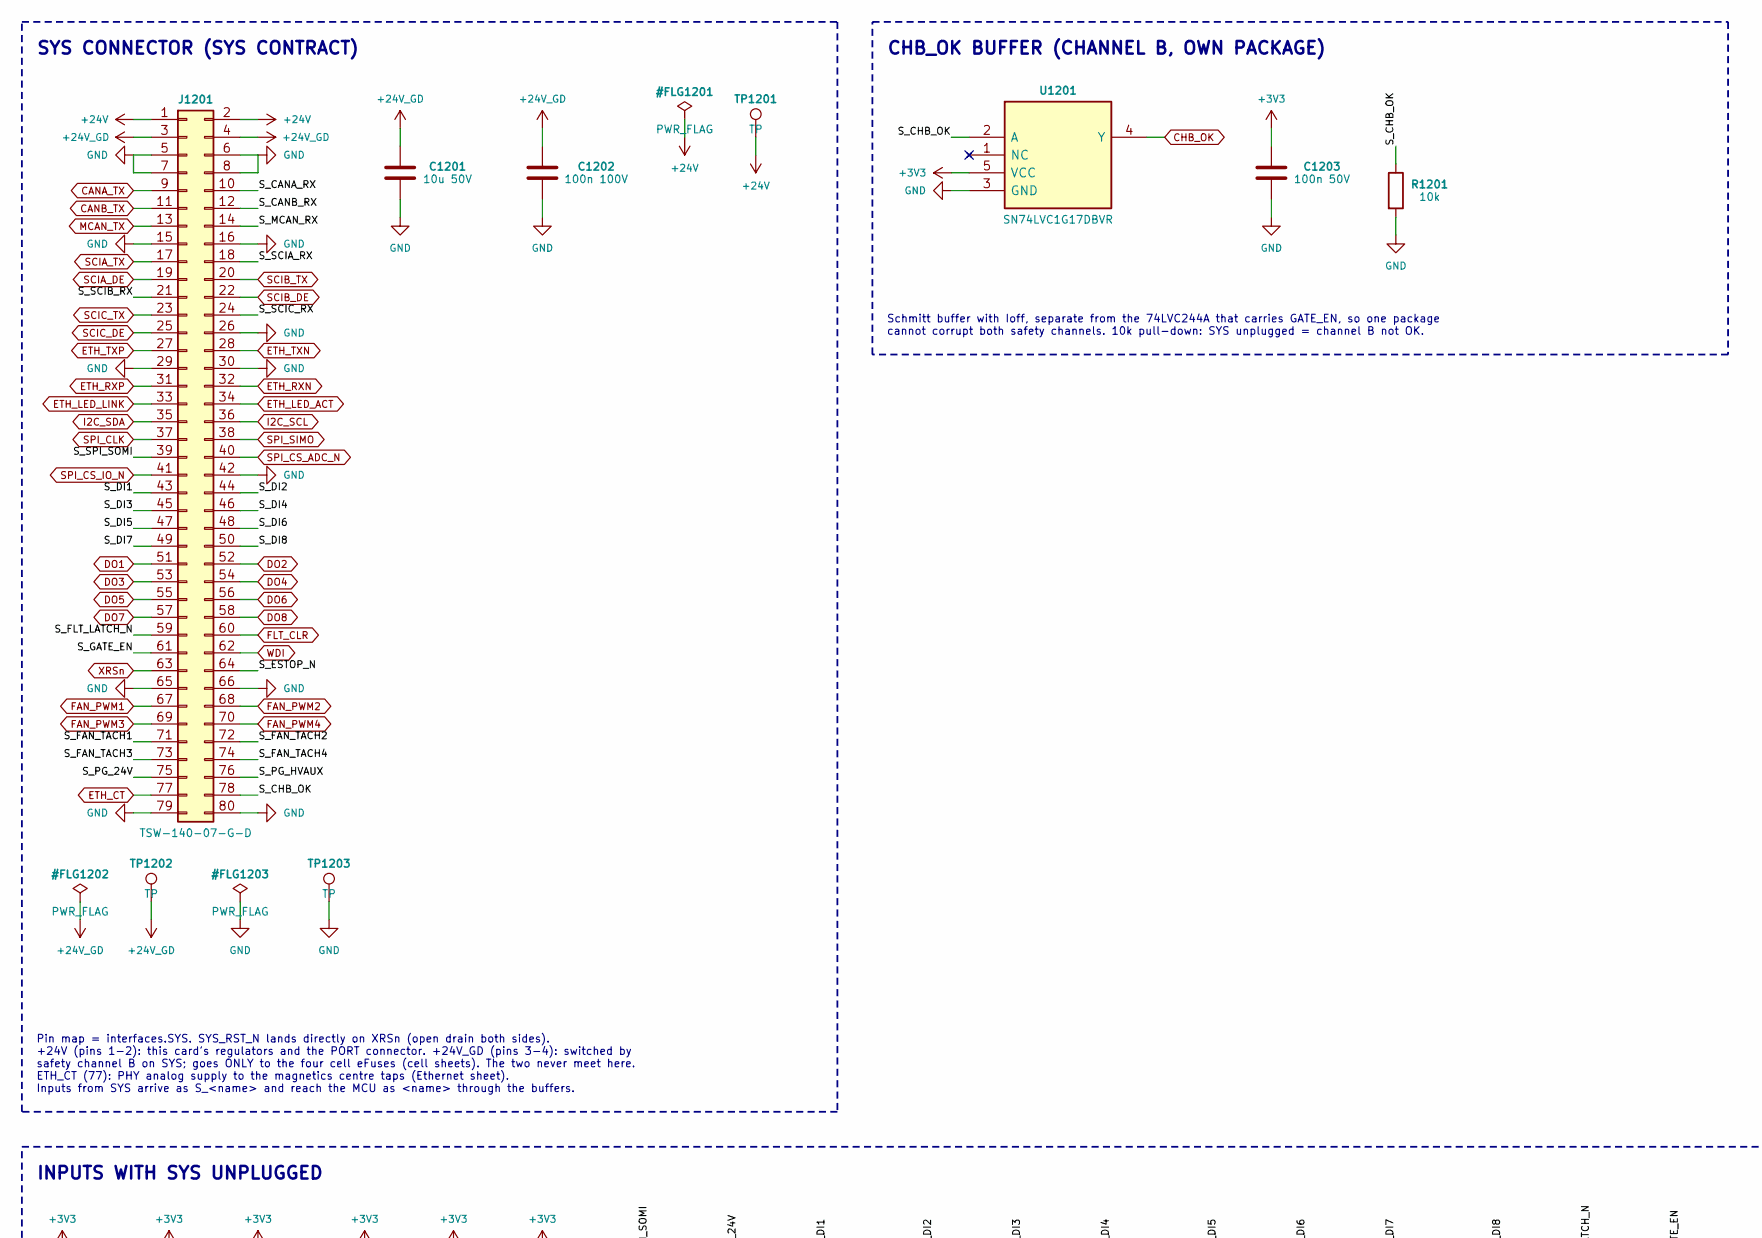
[picture p205: schematic 12_sys.kicad_sch, part in row 1, column 1]

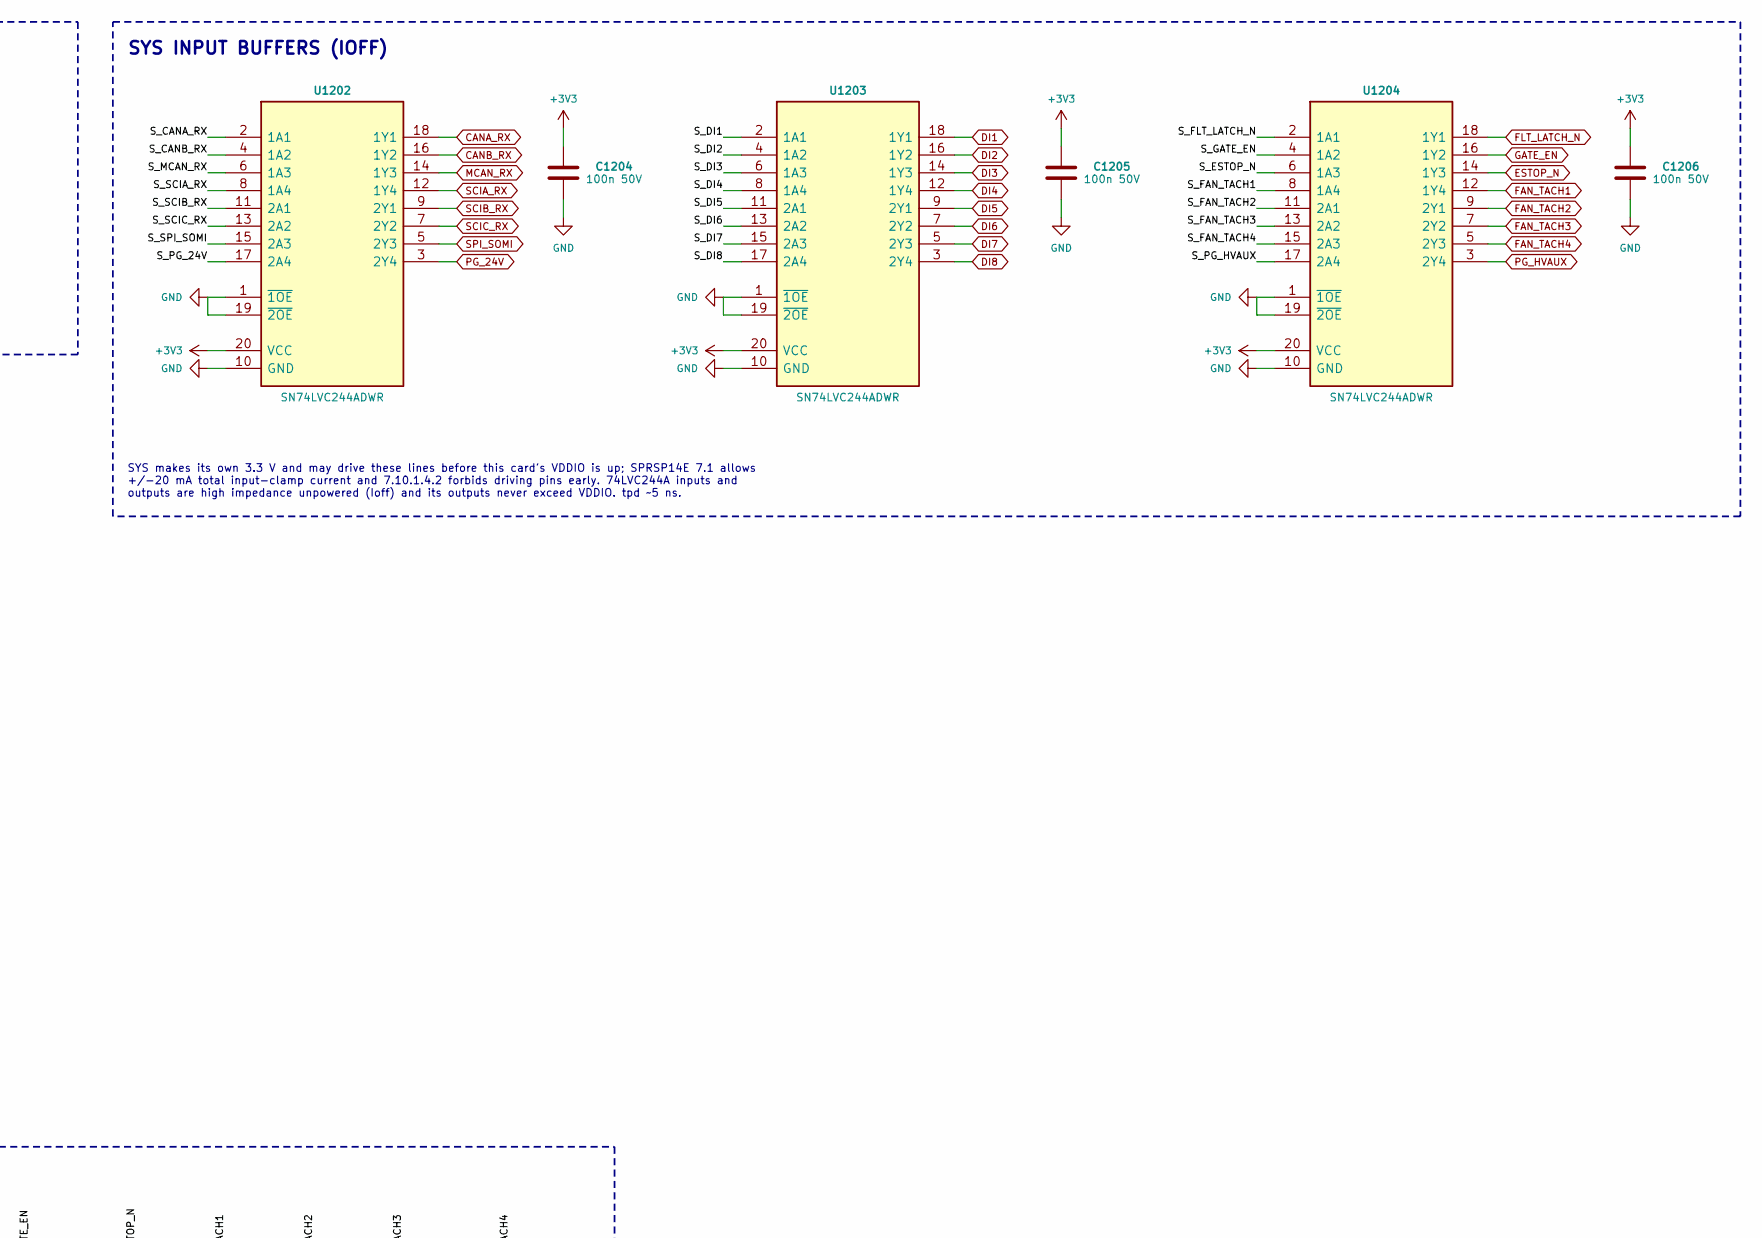
[picture p206: schematic 12_sys.kicad_sch, part in row 1, column 2]

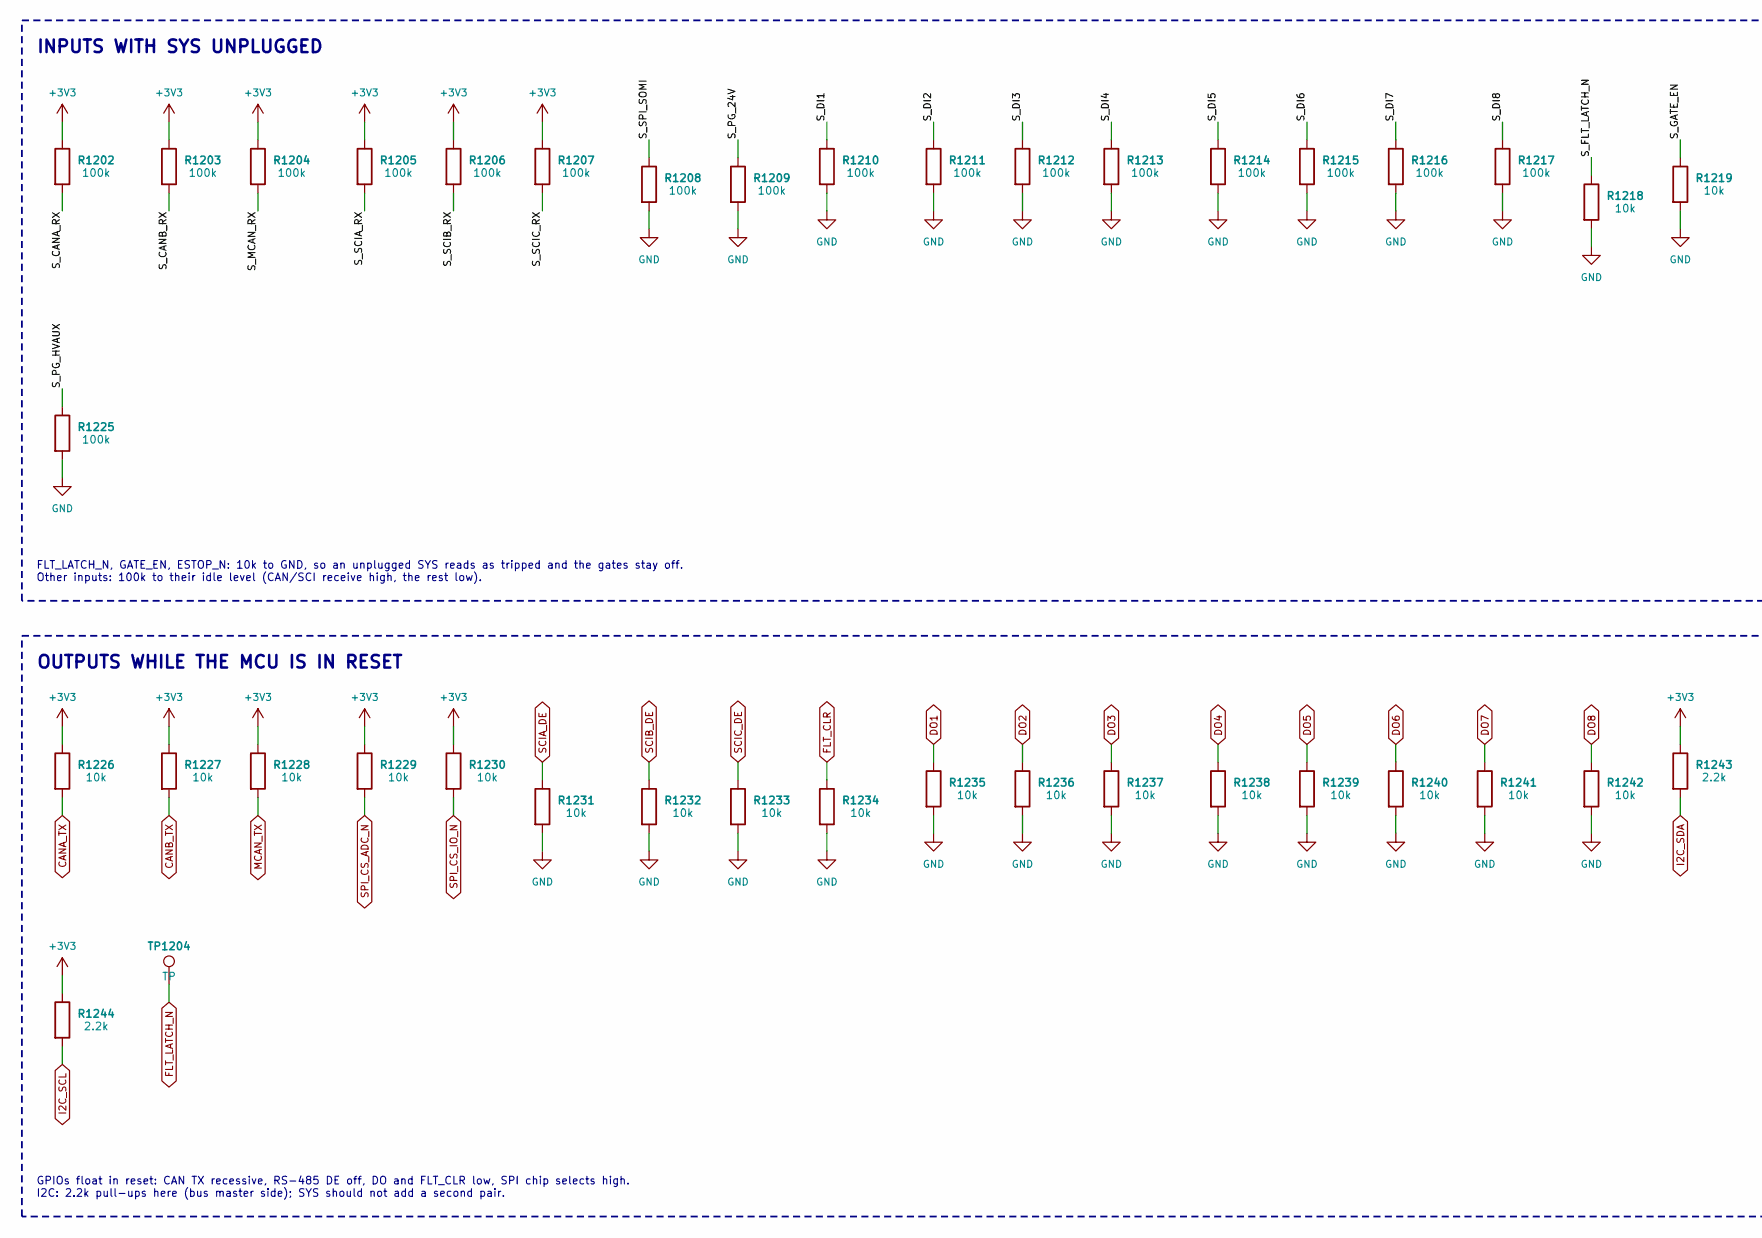
[picture p207: schematic 12_sys.kicad_sch, part in row 2, column 1]

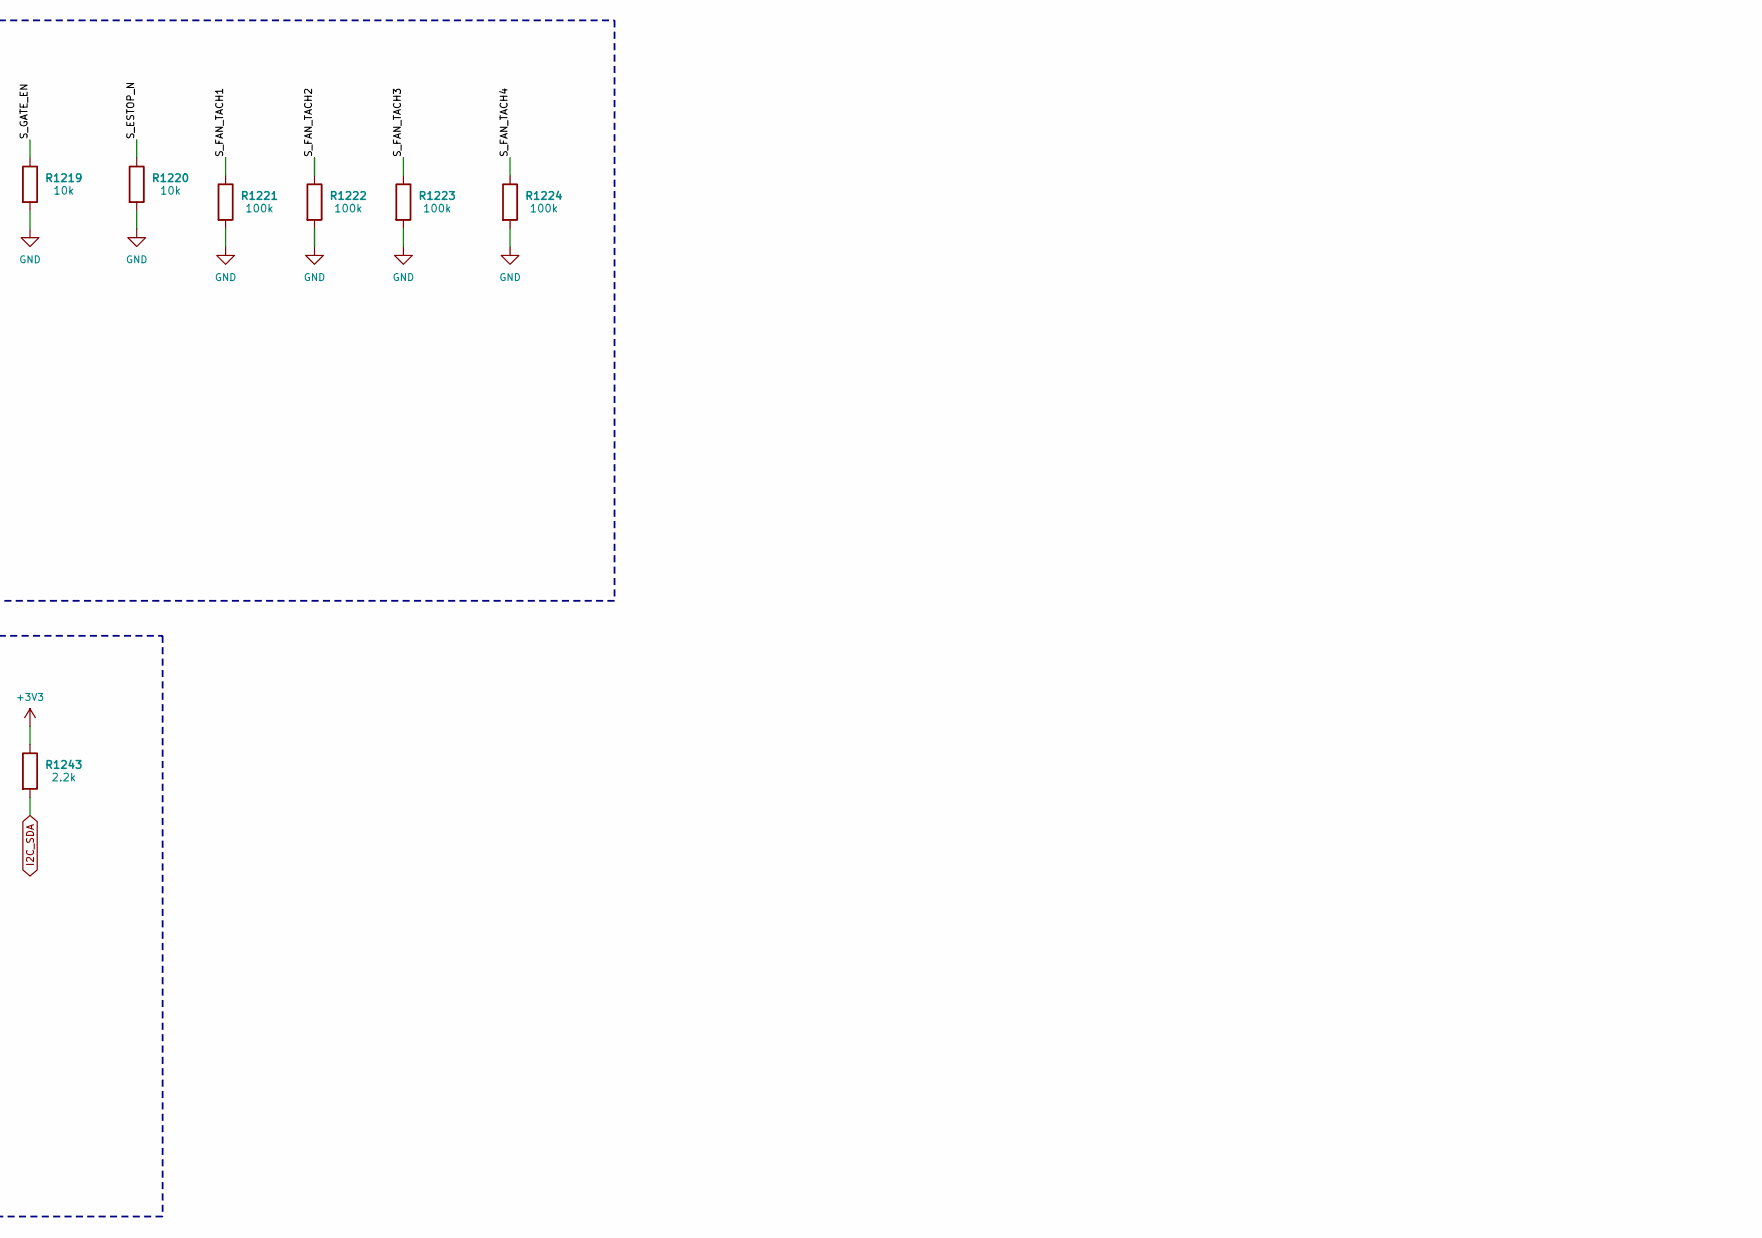
[picture p208: schematic 12_sys.kicad_sch, part in row 2, column 2]

Parts:
C1201: 10u 50V
C1202: 100n 100V
C1203, C1204, C1205, C1206: 100n 50V
J1201: TSW-140-07-G-D; MPN TSW-140-07-G-D
R1201, R1218, R1219, R1220, R1226, R1227, R1228, R1229, R1230, R1231, R1232, R1233, R1234, R1235, R1236, R1237, R1238, R1239, R1240, R1241, R1242: 10k
R1202, R1203, R1204, R1205, R1206, R1207, R1208, R1209, R1210, R1211, R1212, R1213, R1214, R1215, R1216, R1217, R1221, R1222, R1223, R1224, R1225: 100k
R1243, R1244: 2.2k
TP1201, TP1202, TP1203, TP1204: TP
U1201: SN74LVC1G17DBVR; MPN SN74LVC1G17DBVR
U1202, U1203, U1204: SN74LVC244ADWR; MPN SN74LVC244ADWR

Connections:
+3V3: C1203.1, C1204.1, C1205.1, C1206.1, R1202.1, R1203.1, R1204.1, R1205.1, R1206.1, R1207.1, R1226.1, R1227.1, R1228.1, R1229.1, R1230.1, R1243.1, R1244.1, U1201.5 (VCC), U1202.20 (VCC), U1203.20 (VCC), U1204.20 (VCC)
+24V: J1201.1, J1201.2, TP1201.1
+24V_GD: C1201.1, C1202.1, J1201.3, J1201.4, TP1202.1
CANA_RX: U1202.18 (1Y1)
CANA_TX: J1201.9, R1226.2
CANB_RX: U1202.16 (1Y2)
CANB_TX: J1201.11, R1227.2
CHB_OK: U1201.4 (Y)
DI1: U1203.18 (1Y1)
DI2: U1203.16 (1Y2)
DI3: U1203.14 (1Y3)
DI4: U1203.12 (1Y4)
DI5: U1203.9 (2Y1)
DI6: U1203.7 (2Y2)
DI7: U1203.5 (2Y3)
DI8: U1203.3 (2Y4)
DO1: J1201.51, R1235.1
DO2: J1201.52, R1236.1
DO3: J1201.53, R1237.1
DO4: J1201.54, R1238.1
DO5: J1201.55, R1239.1
DO6: J1201.56, R1240.1
DO7: J1201.57, R1241.1
DO8: J1201.58, R1242.1
ESTOP_N: U1204.14 (1Y3)
ETH_CT: J1201.77
ETH_LED_ACT: J1201.34
ETH_LED_LINK: J1201.33
ETH_RXN: J1201.32
ETH_RXP: J1201.31
ETH_TXN: J1201.28
ETH_TXP: J1201.27
FAN_PWM1: J1201.67
FAN_PWM2: J1201.68
FAN_PWM3: J1201.69
FAN_PWM4: J1201.70
FAN_TACH1: U1204.12 (1Y4)
FAN_TACH2: U1204.9 (2Y1)
FAN_TACH3: U1204.7 (2Y2)
FAN_TACH4: U1204.5 (2Y3)
FLT_CLR: J1201.60, R1234.1
FLT_LATCH_N: TP1204.1, U1204.18 (1Y1)
GATE_EN: U1204.16 (1Y2)
GND: C1201.2, C1202.2, C1203.2, C1204.2, C1205.2, C1206.2, J1201.5, J1201.6, J1201.7, J1201.8, J1201.15, J1201.16, J1201.26, J1201.29, J1201.30, J1201.42, J1201.65, J1201.66, J1201.79, J1201.80, R1201.2, R1208.2, R1209.2, R1210.2, R1211.2, R1212.2, R1213.2, R1214.2, R1215.2, R1216.2, R1217.2, R1218.2, R1219.2, R1220.2, R1221.2, R1222.2, R1223.2, R1224.2, R1225.2, R1231.2, R1232.2, R1233.2, R1234.2, R1235.2, R1236.2, R1237.2, R1238.2, R1239.2, R1240.2, R1241.2, R1242.2, TP1203.1, U1201.3 (GND), U1202.1 (~1OE), U1202.10 (GND), U1202.19 (~2OE), U1203.1 (~1OE), U1203.10 (GND), U1203.19 (~2OE), U1204.1 (~1OE), U1204.10 (GND), U1204.19 (~2OE)
I2C_SCL: J1201.36, R1244.2
I2C_SDA: J1201.35, R1243.2
MCAN_RX: U1202.14 (1Y3)
MCAN_TX: J1201.13, R1228.2
PG_24V: U1202.3 (2Y4)
PG_HVAUX: U1204.3 (2Y4)
SCIA_DE: J1201.19, R1231.1
SCIA_RX: U1202.12 (1Y4)
SCIA_TX: J1201.17
SCIB_DE: J1201.22, R1232.1
SCIB_RX: U1202.9 (2Y1)
SCIB_TX: J1201.20
SCIC_DE: J1201.25, R1233.1
SCIC_RX: U1202.7 (2Y2)
SCIC_TX: J1201.23
SPI_CLK: J1201.37
SPI_CS_ADC_N: J1201.40, R1229.2
SPI_CS_IO_N: J1201.41, R1230.2
SPI_SIMO: J1201.38
SPI_SOMI: U1202.5 (2Y3)
S_CANA_RX: J1201.10, R1202.2, U1202.2 (1A1)
S_CANB_RX: J1201.12, R1203.2, U1202.4 (1A2)
S_CHB_OK: J1201.78, R1201.1, U1201.2 (A)
S_DI1: J1201.43, R1210.1, U1203.2 (1A1)
S_DI2: J1201.44, R1211.1, U1203.4 (1A2)
S_DI3: J1201.45, R1212.1, U1203.6 (1A3)
S_DI4: J1201.46, R1213.1, U1203.8 (1A4)
S_DI5: J1201.47, R1214.1, U1203.11 (2A1)
S_DI6: J1201.48, R1215.1, U1203.13 (2A2)
S_DI7: J1201.49, R1216.1, U1203.15 (2A3)
S_DI8: J1201.50, R1217.1, U1203.17 (2A4)
S_ESTOP_N: J1201.64, R1220.1, U1204.6 (1A3)
S_FAN_TACH1: J1201.71, R1221.1, U1204.8 (1A4)
S_FAN_TACH2: J1201.72, R1222.1, U1204.11 (2A1)
S_FAN_TACH3: J1201.73, R1223.1, U1204.13 (2A2)
S_FAN_TACH4: J1201.74, R1224.1, U1204.15 (2A3)
S_FLT_LATCH_N: J1201.59, R1218.1, U1204.2 (1A1)
S_GATE_EN: J1201.61, R1219.1, U1204.4 (1A2)
S_MCAN_RX: J1201.14, R1204.2, U1202.6 (1A3)
S_PG_24V: J1201.75, R1209.1, U1202.17 (2A4)
S_PG_HVAUX: J1201.76, R1225.1, U1204.17 (2A4)
S_SCIA_RX: J1201.18, R1205.2, U1202.8 (1A4)
S_SCIB_RX: J1201.21, R1206.2, U1202.11 (2A1)
S_SCIC_RX: J1201.24, R1207.2, U1202.13 (2A2)
S_SPI_SOMI: J1201.39, R1208.1, U1202.15 (2A3)
WDI: J1201.62
XRSn: J1201.63

Notes on the sheet:
Pin map = interfaces.SYS. SYS_RST_N lands directly on XRSn (open drain both sides). +24V (pins 1-2): this card's regulators and the PORT connector. +24V_GD (pins 3-4): switched by safety channel B on SYS; goes ONLY to the four cell eFuses (cell sheets). The two never meet here. ETH_CT (77): PHY ana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
INPUTS WITH SYS UNPLUGGED
CHB_OK BUFFER (CHANNEL B, OWN PACKAGE)
SYS CONNECTOR (SYS CONTRACT)
Schmitt buffer with Ioff, separate from the 74LVC244A that carries GATE_EN, so one package cannot corrupt both safety channels. 10k pull-down: SYS unplugged = channel B not OK.
OUTPUTS WHILE THE MCU IS IN RESET
SYS makes its own 3.3 V and may drive these lines before this card's VDDIO is up; SPRSP14E 7.1 allows +/-20 mA total input-clamp current and 7.10.1.4.2 forbids driving pins early. 74LVC244A inputs and outputs are high impedance unpowered (Ioff) and its outputs never exceed VDDIO. tpd ~5 ns.
SYS INPUT BUFFERS (IOFF)
GPIOs float in reset: CAN TX recessive, RS-485 DE off, DO and FLT_CLR low, SPI chip selects high. I2C: 2.2k pull-ups here (bus master side); SYS should not add a second pair.
FLT_LATCH_N, GATE_EN, ESTOP_N: 10k to GND, so an unplugged SYS reads as tripped and the gates stay off. Other inputs: 100k to their idle level (CAN/SCI receive high, the rest low).
