vectivolt/PCM/hardware/CTRL-C2000/sheets/13_eth.kicad_sch

## KiCad design hardware/CTRL-C2000/sheets/13_eth.kicad_sch (2026-10-04)

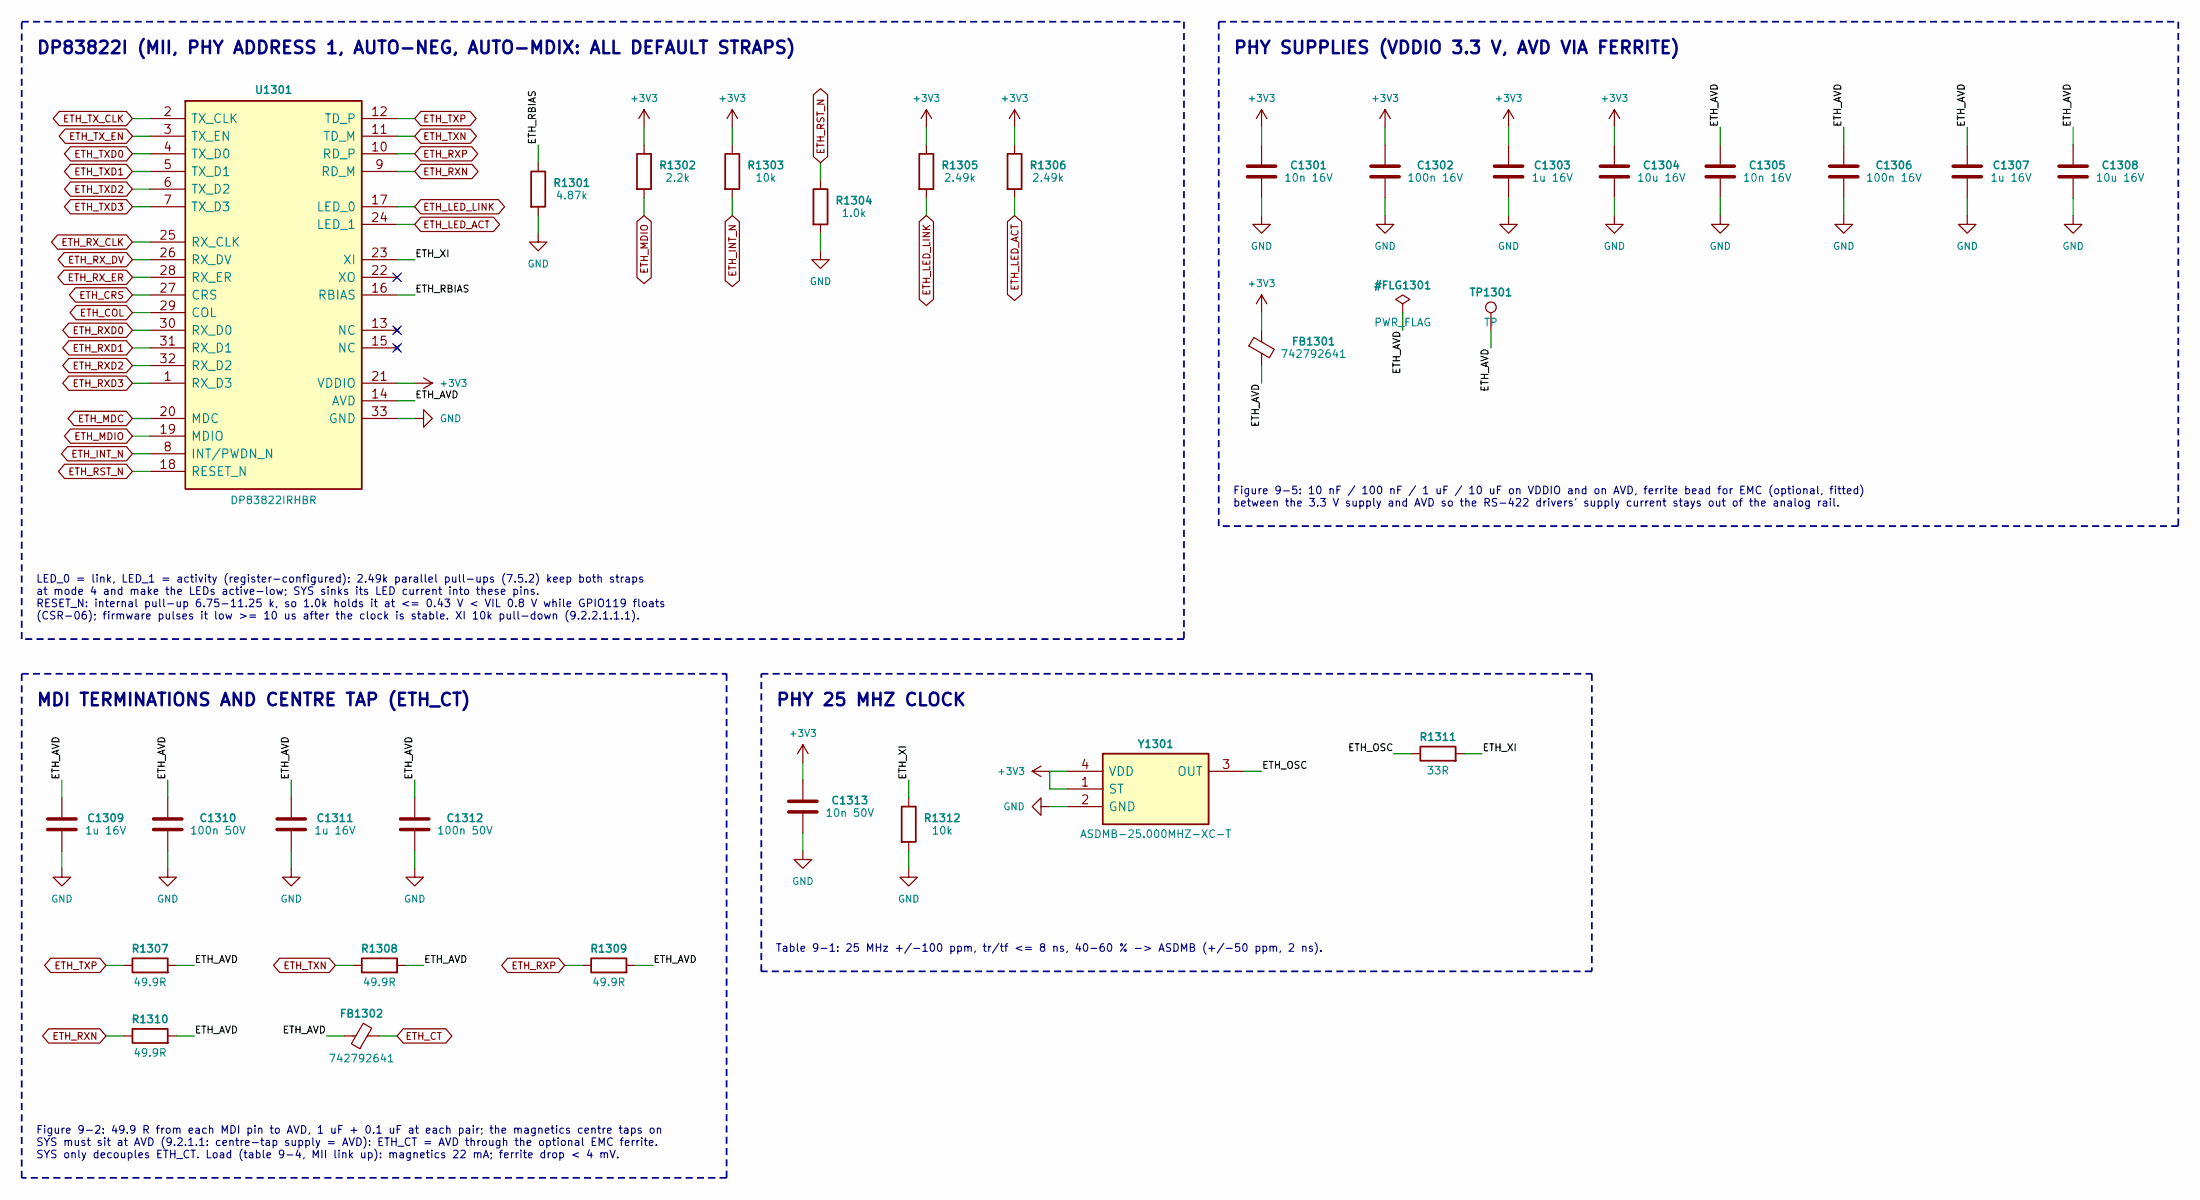
[picture p209: schematic 13_eth.kicad_sch]

Parts:
C1301, C1305: 10n 16V
C1302, C1306: 100n 16V
C1303, C1307, C1309, C1311: 1u 16V
C1304, C1308: 10u 16V
C1310, C1312: 100n 50V
C1313: 10n 50V
FB1301, FB1302: 742792641; MPN 742792641
R1301: 4.87k
R1302: 2.2k
R1303, R1312: 10k
R1304: 1.0k
R1305, R1306: 2.49k
R1307, R1308, R1309, R1310: 49.9R
R1311: 33R
TP1301: TP
U1301: DP83822IRHBR; MPN DP83822IRHBR
Y1301: ASDMB-25.000MHZ-XC-T; MPN ASDMB-25.000MHZ-XC-T

Connections:
+3V3: C1301.1, C1302.1, C1303.1, C1304.1, C1313.1, FB1301.1, R1302.1, R1303.1, R1305.1, R1306.1, U1301.21 (VDDIO), Y1301.1 (ST), Y1301.4 (VDD)
ETH_AVD: C1305.1, C1306.1, C1307.1, C1308.1, C1309.1, C1310.1, C1311.1, C1312.1, FB1301.2, FB1302.1, R1307.2, R1308.2, R1309.2, R1310.2, TP1301.1, U1301.14 (AVD)
ETH_COL: U1301.29 (COL)
ETH_CRS: U1301.27 (CRS)
ETH_CT: FB1302.2
ETH_INT_N: R1303.2, U1301.8 (INT/PWDN_N)
ETH_LED_ACT: R1306.2, U1301.24 (LED_1)
ETH_LED_LINK: R1305.2, U1301.17 (LED_0)
ETH_MDC: U1301.20 (MDC)
ETH_MDIO: R1302.2, U1301.19 (MDIO)
ETH_OSC: R1311.1, Y1301.3 (OUT)
ETH_RBIAS: R1301.1, U1301.16 (RBIAS)
ETH_RST_N: R1304.1, U1301.18 (RESET_N)
ETH_RXD0: U1301.30 (RX_D0)
ETH_RXD1: U1301.31 (RX_D1)
ETH_RXD2: U1301.32 (RX_D2)
ETH_RXD3: U1301.1 (RX_D3)
ETH_RXN: R1310.1, U1301.9 (RD_M)
ETH_RXP: R1309.1, U1301.10 (RD_P)
ETH_RX_CLK: U1301.25 (RX_CLK)
ETH_RX_DV: U1301.26 (RX_DV)
ETH_RX_ER: U1301.28 (RX_ER)
ETH_TXD0: U1301.4 (TX_D0)
ETH_TXD1: U1301.5 (TX_D1)
ETH_TXD2: U1301.6 (TX_D2)
ETH_TXD3: U1301.7 (TX_D3)
ETH_TXN: R1308.1, U1301.11 (TD_M)
ETH_TXP: R1307.1, U1301.12 (TD_P)
ETH_TX_CLK: U1301.2 (TX_CLK)
ETH_TX_EN: U1301.3 (TX_EN)
ETH_XI: R1311.2, R1312.1, U1301.23 (XI)
GND: C1301.2, C1302.2, C1303.2, C1304.2, C1305.2, C1306.2, C1307.2, C1308.2, C1309.2, C1310.2, C1311.2, C1312.2, C1313.2, R1301.2, R1304.2, R1312.2, U1301.33 (GND), Y1301.2 (GND)

Notes on the sheet:
LED_0 = link, LED_1 = activity (register-configured): 2.49k parallel pull-ups (7.5.2) keep both straps at mode 4 and make the LEDs active-low; SYS sinks its LED current into these pins. RESET_N: internal pull-up 6.75-11.25 k, so 1.0k holds it at <= 0.43 V < VIL 0.8 V while GPIO119 floats (CSR-06); 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
PHY 25 MHZ CLOCK
PHY SUPPLIES (VDDIO 3.3 V, AVD VIA FERRITE)
Table 9-1: 25 MHz +/-100 ppm, tr/tf <= 8 ns, 40-60 % -> ASDMB (+/-50 ppm, 2 ns).
DP83822I (MII, PHY ADDRESS 1, AUTO-NEG, AUTO-MDIX: ALL DEFAULT STRAPS)
Figure 9-5: 10 nF / 100 nF / 1 uF / 10 uF on VDDIO and on AVD, ferrite bead for EMC (optional, fitted) between the 3.3 V supply and AVD so the RS-422 drivers' supply current stays out of the analog rail.
MDI TERMINATIONS AND CENTRE TAP (ETH_CT)
Figure 9-2: 49.9 R from each MDI pin to AVD, 1 uF + 0.1 uF at each pair; the magnetics centre taps on SYS must sit at AVD (9.2.1.1: centre-tap supply = AVD): ETH_CT = AVD through the optional EMC ferrite. SYS only decouples ETH_CT. Load (table 9-4, MII link up): magnetics 22 mA; ferrite drop < 4 mV.
