vectivolt/PCM/hardware/CTRL-C2000/sheets/14_debug.kicad_sch

## KiCad design hardware/CTRL-C2000/sheets/14_debug.kicad_sch (2026-10-04)

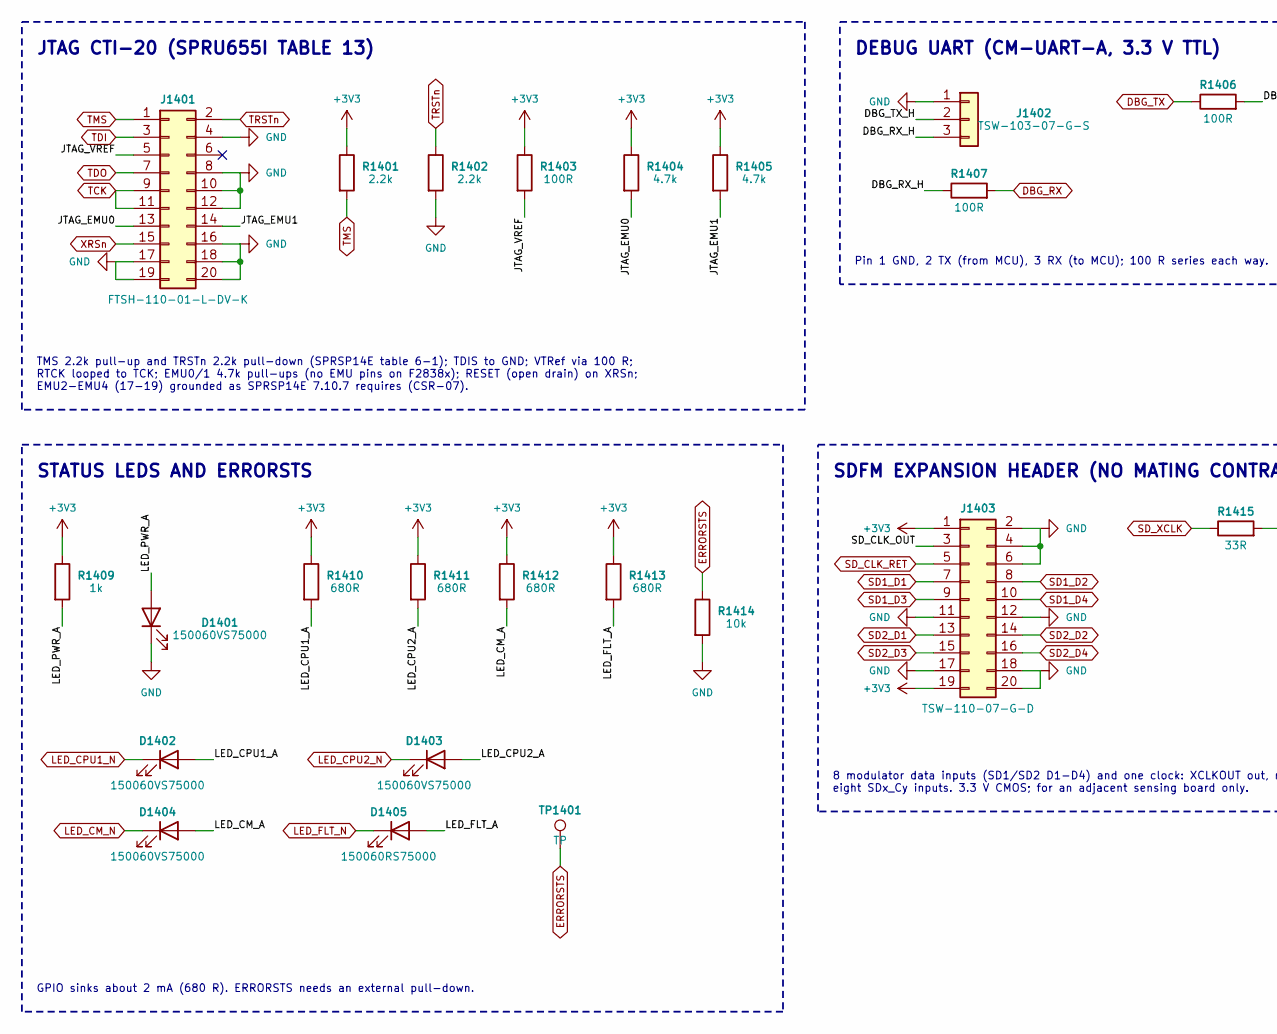
[picture p210: schematic 14_debug.kicad_sch, part in row 1, column 1]

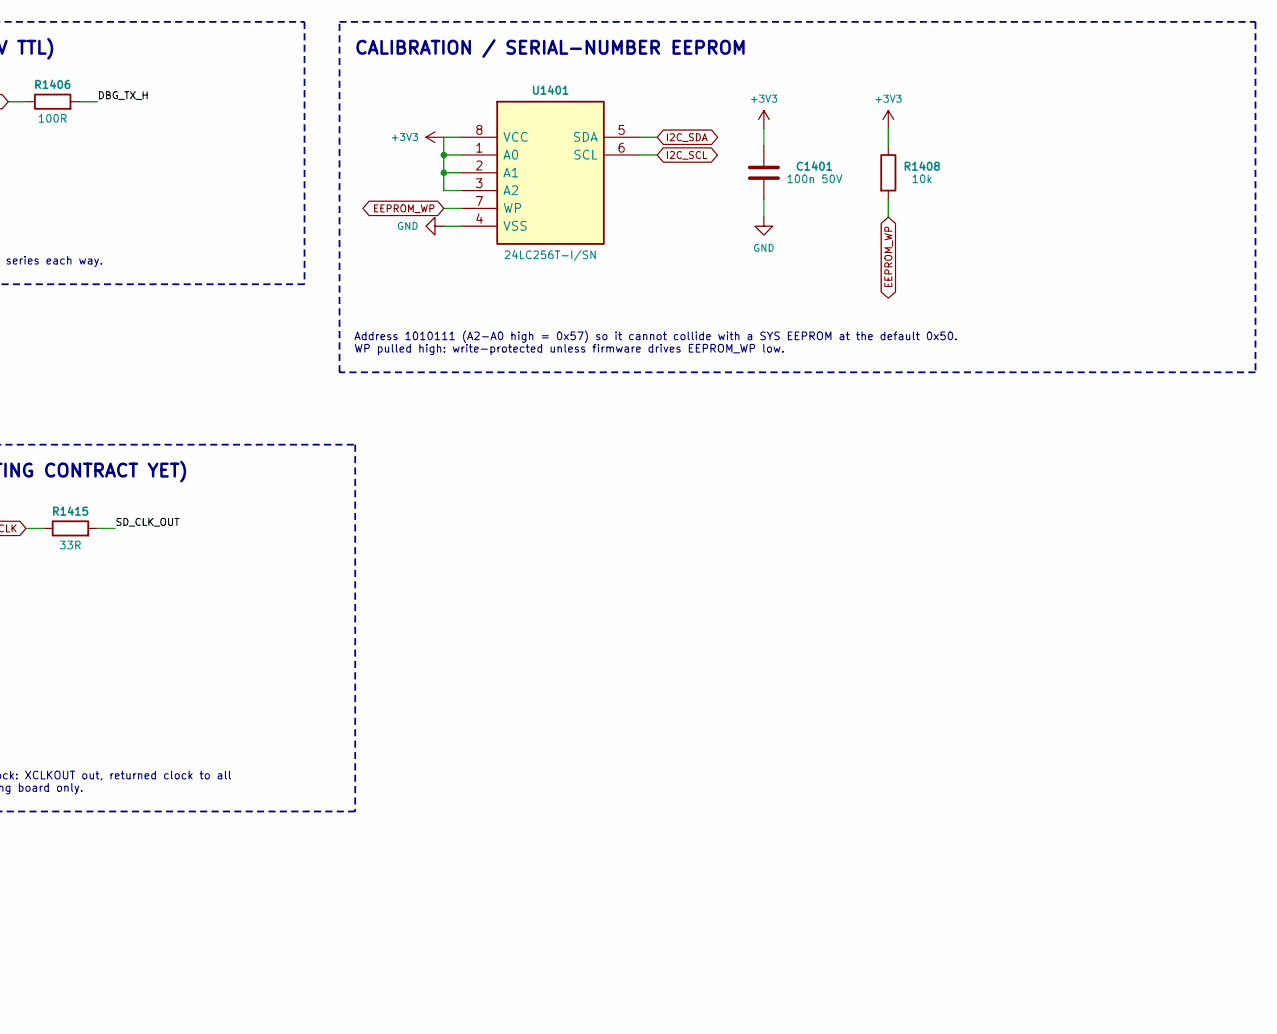
[picture p211: schematic 14_debug.kicad_sch, part in row 1, column 2]

Parts:
C1401: 100n 50V
D1401, D1402, D1403, D1404: 150060VS75000; MPN 150060VS75000
D1405: 150060RS75000; MPN 150060RS75000
J1401: FTSH-110-01-L-DV-K; MPN FTSH-110-01-L-DV-K
J1402: TSW-103-07-G-S; MPN TSW-103-07-G-S
J1403: TSW-110-07-G-D; MPN TSW-110-07-G-D
R1401, R1402: 2.2k
R1403, R1406, R1407: 100R
R1404, R1405: 4.7k
R1408, R1414: 10k
R1409: 1k
R1410, R1411, R1412, R1413: 680R
R1415: 33R
TP1401: TP
U1401: 24LC256T-I/SN; MPN 24LC256T-I/SN

Connections:
+3V3: C1401.1, J1403.1, J1403.19, R1401.1, R1403.1, R1404.1, R1405.1, R1408.1, R1409.1, R1410.1, R1411.1, R1412.1, R1413.1, U1401.1 (A0), U1401.2 (A1), U1401.3 (A2), U1401.8 (VCC)
DBG_RX: R1407.2
DBG_RX_H: J1402.3, R1407.1
DBG_TX: R1406.1
DBG_TX_H: J1402.2, R1406.2
EEPROM_WP: R1408.2, U1401.7 (WP)
ERRORSTS: R1414.1, TP1401.1
GND: C1401.2, D1401.1 (K), J1401.4, J1401.8, J1401.10, J1401.12, J1401.16, J1401.17, J1401.18, J1401.19, J1401.20, J1402.1, J1403.2, J1403.4, J1403.6, J1403.11, J1403.12, J1403.17, J1403.18, J1403.20, R1402.2, R1414.2, U1401.4 (VSS)
I2C_SCL: U1401.6 (SCL)
I2C_SDA: U1401.5 (SDA)
JTAG_EMU0: J1401.13, R1404.2
JTAG_EMU1: J1401.14, R1405.2
JTAG_VREF: J1401.5, R1403.2
LED_CM_A: D1404.2 (A), R1412.2
LED_CM_N: D1404.1 (K)
LED_CPU1_A: D1402.2 (A), R1410.2
LED_CPU1_N: D1402.1 (K)
LED_CPU2_A: D1403.2 (A), R1411.2
LED_CPU2_N: D1403.1 (K)
LED_FLT_A: D1405.2 (A), R1413.2
LED_FLT_N: D1405.1 (K)
LED_PWR_A: D1401.2 (A), R1409.2
SD1_D1: J1403.7
SD1_D2: J1403.8
SD1_D3: J1403.9
SD1_D4: J1403.10
SD2_D1: J1403.13
SD2_D2: J1403.14
SD2_D3: J1403.15
SD2_D4: J1403.16
SD_CLK_OUT: J1403.3, R1415.2
SD_CLK_RET: J1403.5
SD_XCLK: R1415.1
TCK: J1401.9, J1401.11
TDI: J1401.3
TDO: J1401.7
TMS: J1401.1, R1401.2
TRSTn: J1401.2, R1402.1
XRSn: J1401.15

Notes on the sheet:
GPIO sinks about 2 mA (680 R). ERRORSTS needs an external pull-down.
8 modulator data inputs (SD1/SD2 D1-D4) and one clock: XCLKOUT out, returned clock to all eight SDx_Cy inputs. 3.3 V CMOS; for an adjacent sensing board only.
Pin 1 GND, 2 TX (from MCU), 3 RX (to MCU); 100 R series each way.
DEBUG UART (CM-UART-A, 3.3 V TTL)
TMS 2.2k pull-up and TRSTn 2.2k pull-down (SPRSP14E table 6-1); TDIS to GND; VTRef via 100 R; RTCK looped to TCK; EMU0/1 4.7k pull-ups (no EMU pins on F2838x); RESET (open drain) on XRSn; EMU2-EMU4 (17-19) grounded as SPRSP14E 7.10.7 requires (CSR-07).
CALIBRATION / SERIAL-NUMBER EEPROM
JTAG CTI-20 (SPRU655I TABLE 13)
SDFM EXPANSION HEADER (NO MATING CONTRACT YET)
Address 1010111 (A2-A0 high = 0x57) so it cannot collide with a SYS EEPROM at the default 0x50. WP pulled high: write-protected unless firmware drives EEPROM_WP low.
STATUS LEDS AND ERRORSTS
