vectivolt/PCM/hardware/DAB60/sheets/01_b1_power.kicad_sch

## KiCad design hardware/DAB60/sheets/01_b1_power.kicad_sch (2026-10-04)

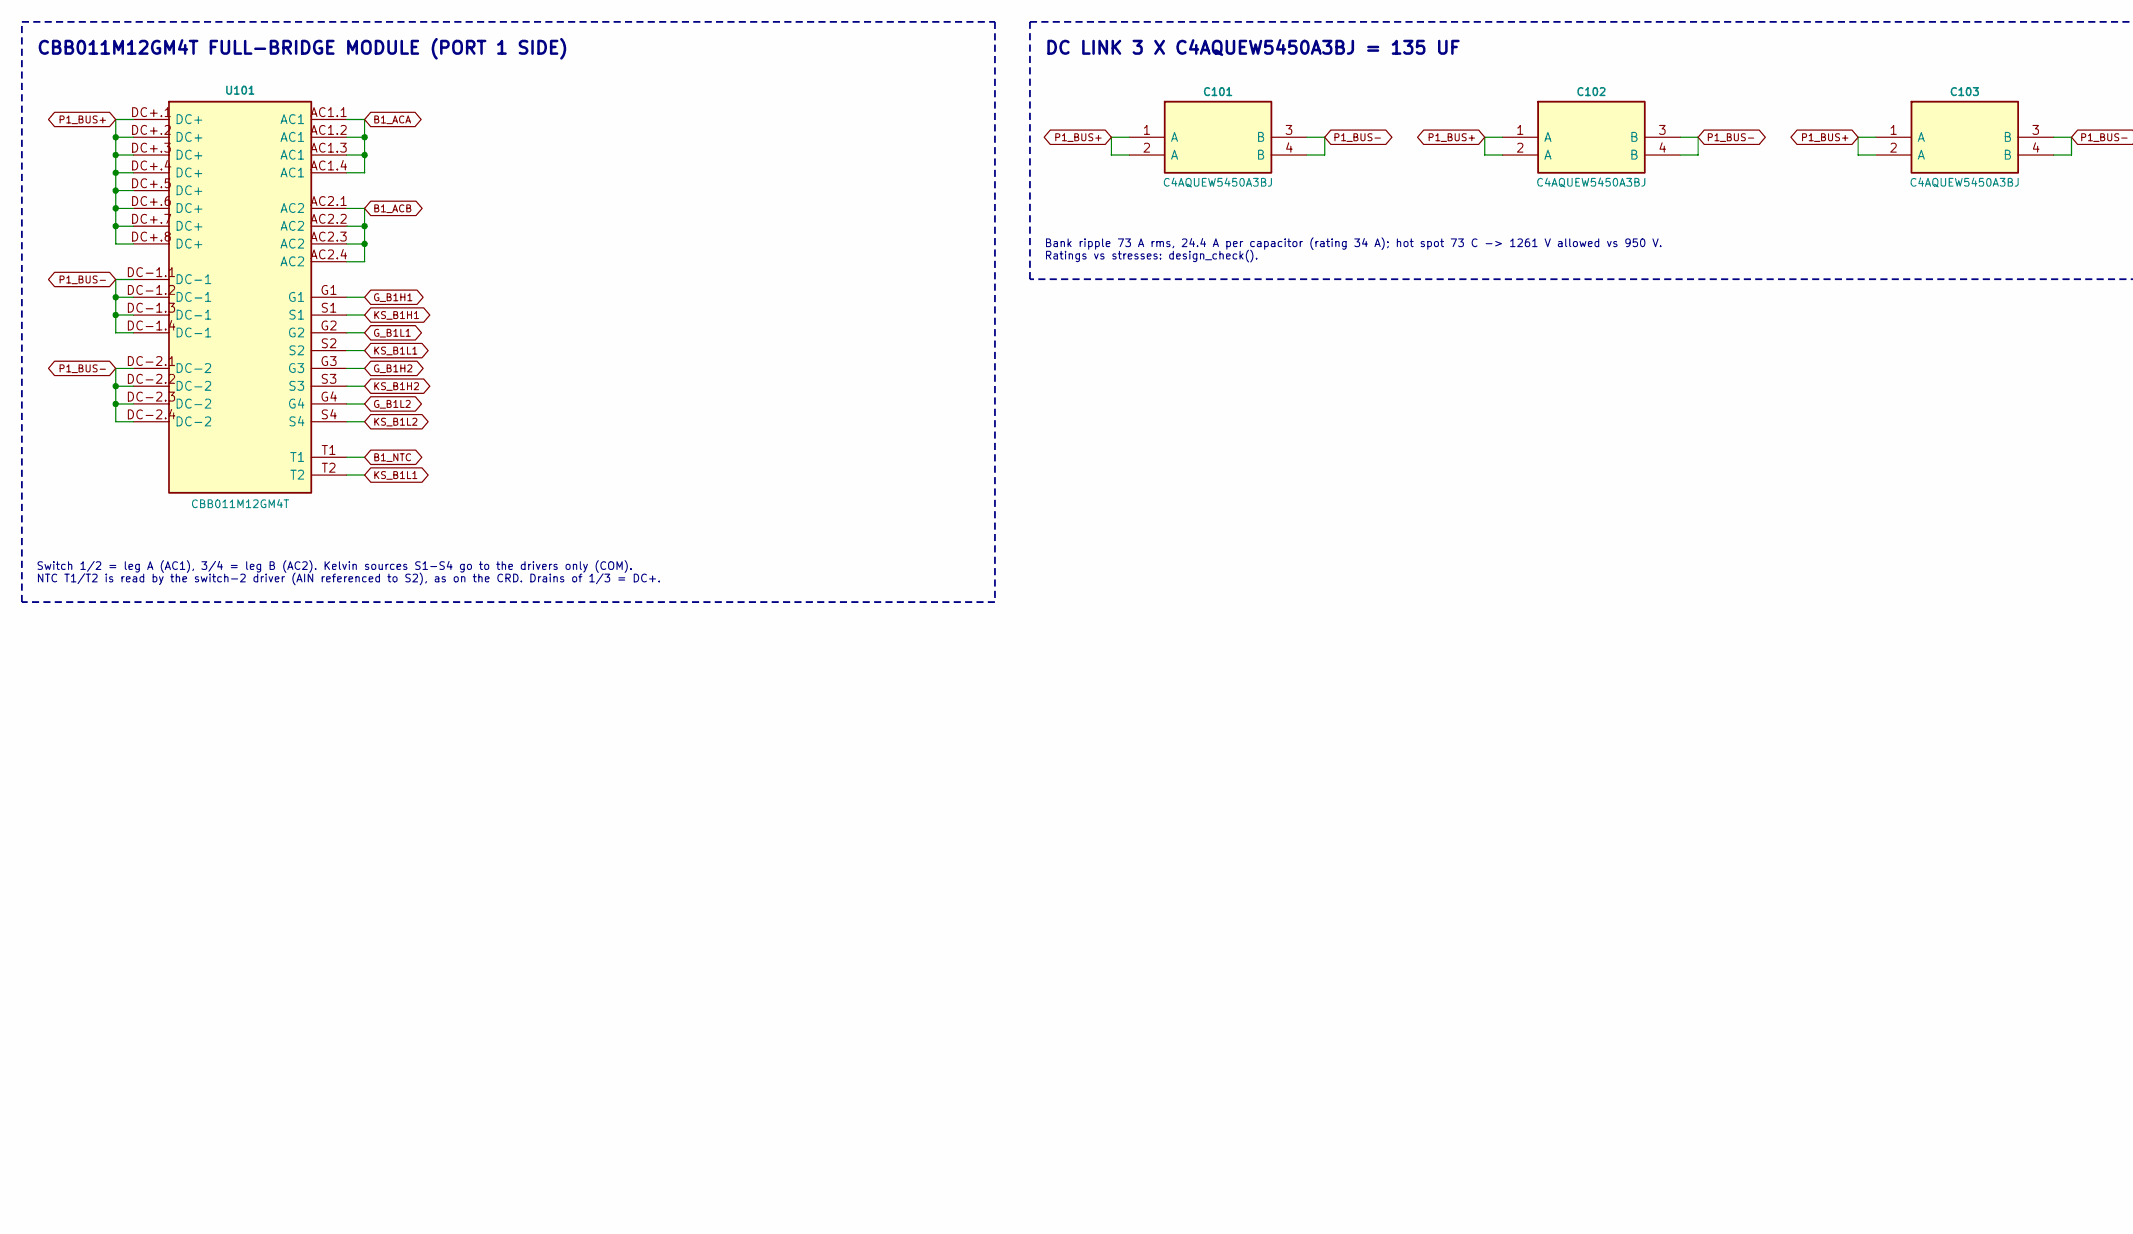
[picture p212: schematic 01_b1_power.kicad_sch, part in row 1, column 1]

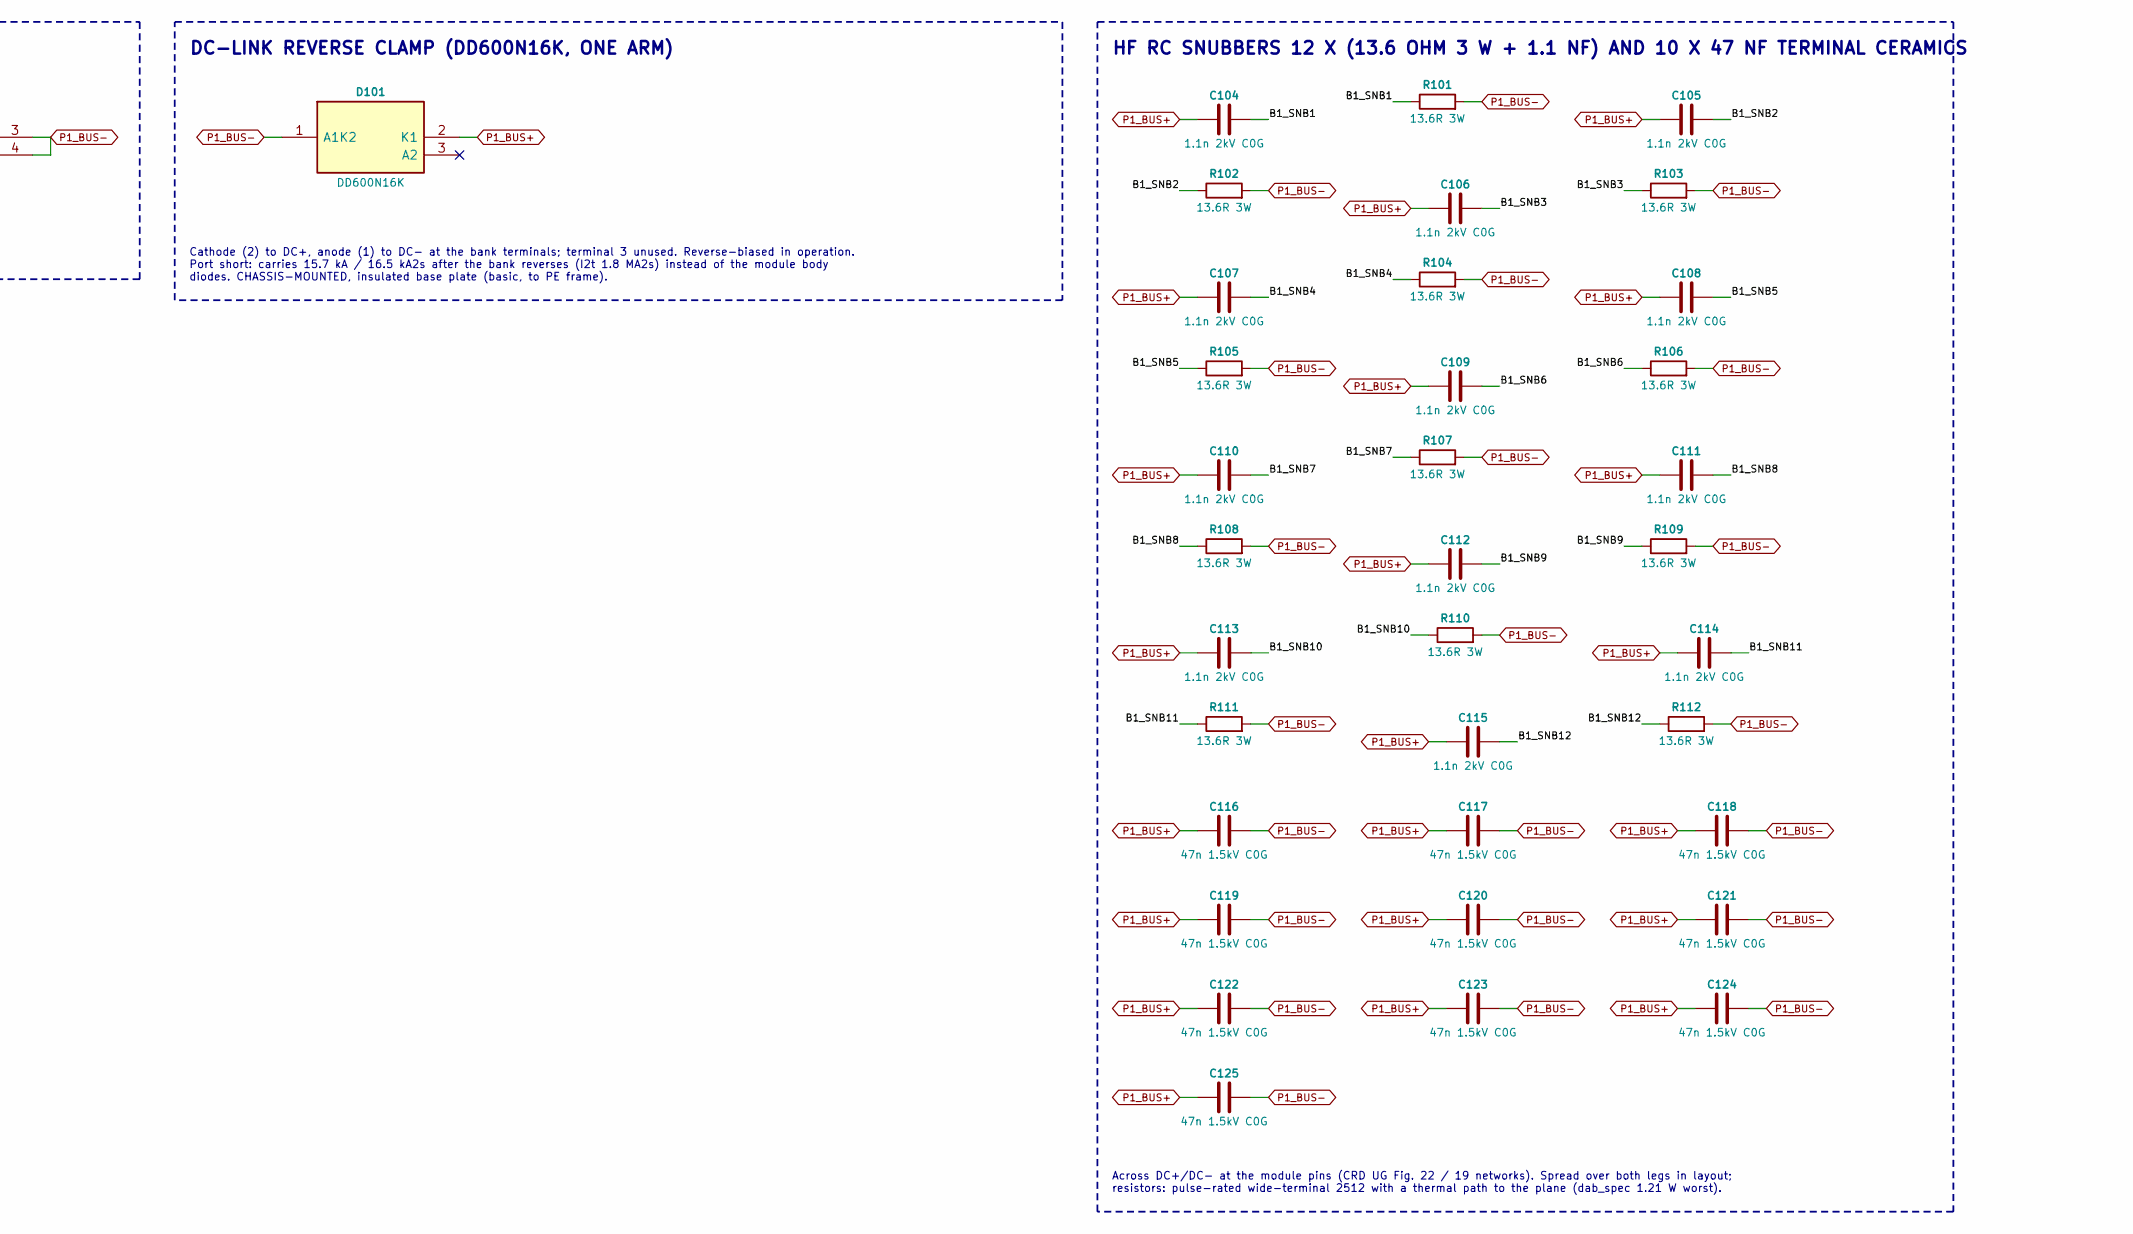
[picture p213: schematic 01_b1_power.kicad_sch, part in row 1, column 2]

Parts:
C101, C102, C103: C4AQUEW5450A3BJ; MPN C4AQUEW5450A3BJ
C104, C105, C106, C107, C108, C109, C110, C111, C112, C113, C114, C115: 1.1n 2kV C0G
C116, C117, C118, C119, C120, C121, C122, C123, C124, C125: 47n 1.5kV C0G
D101: DD600N16K; MPN DD600N16K
R101, R102, R103, R104, R105, R106, R107, R108, R109, R110, R111, R112: 13.6R 3W
U101: CBB011M12GM4T; MPN CBB011M12GM4T

Connections:
B1_ACA: U101.AC1.1 (AC1), U101.AC1.2 (AC1), U101.AC1.3 (AC1), U101.AC1.4 (AC1)
B1_ACB: U101.AC2.1 (AC2), U101.AC2.2 (AC2), U101.AC2.3 (AC2), U101.AC2.4 (AC2)
B1_NTC: U101.T1
B1_SNB1: C104.2, R101.1
B1_SNB2: C105.2, R102.1
B1_SNB3: C106.2, R103.1
B1_SNB4: C107.2, R104.1
B1_SNB5: C108.2, R105.1
B1_SNB6: C109.2, R106.1
B1_SNB7: C110.2, R107.1
B1_SNB8: C111.2, R108.1
B1_SNB9: C112.2, R109.1
B1_SNB10: C113.2, R110.1
B1_SNB11: C114.2, R111.1
B1_SNB12: C115.2, R112.1
G_B1H1: U101.G1
G_B1H2: U101.G3
G_B1L1: U101.G2
G_B1L2: U101.G4
KS_B1H1: U101.S1
KS_B1H2: U101.S3
KS_B1L1: U101.S2, U101.T2
KS_B1L2: U101.S4
P1_BUS+: C101.1 (A), C101.2 (A), C102.1 (A), C102.2 (A), C103.1 (A), C103.2 (A), C104.1, C105.1, C106.1, C107.1, C108.1, C109.1, C110.1, C111.1, C112.1, C113.1, C114.1, C115.1, C116.1, C117.1, C118.1, C119.1, C120.1, C121.1, C122.1, C123.1, C124.1, C125.1, D101.2 (K1), U101.DC+.1 (DC+), U101.DC+.2 (DC+), U101.DC+.3 (DC+), U101.DC+.4 (DC+), U101.DC+.5 (DC+), U101.DC+.6 (DC+), U101.DC+.7 (DC+), U101.DC+.8 (DC+)
P1_BUS-: C101.3 (B), C101.4 (B), C102.3 (B), C102.4 (B), C103.3 (B), C103.4 (B), C116.2, C117.2, C118.2, C119.2, C120.2, C121.2, C122.2, C123.2, C124.2, C125.2, D101.1 (A1K2), R101.2, R102.2, R103.2, R104.2, R105.2, R106.2, R107.2, R108.2, R109.2, R110.2, R111.2, R112.2, U101.DC-1.1 (DC-1), U101.DC-1.2 (DC-1), U101.DC-1.3 (DC-1), U101.DC-1.4 (DC-1), U101.DC-2.1 (DC-2), U101.DC-2.2 (DC-2), U101.DC-2.3 (DC-2), U101.DC-2.4 (DC-2)

Notes on the sheet:
DC-LINK REVERSE CLAMP (DD600N16K, ONE ARM)
Across DC+/DC- at the module pins (CRD UG Fig. 22 / 19 networks). Spread over both legs in layout; resistors: pulse-rated wide-terminal 2512 with a thermal path to the plane (dab_spec 1.21 W worst).
CBB011M12GM4T FULL-BRIDGE MODULE (PORT 1 SIDE)
Bank ripple 73 A rms, 24.4 A per capacitor (rating 34 A); hot spot 73 C -> 1261 V allowed vs 950 V. Ratings vs stresses: design_check().
DC LINK 3 X C4AQUEW5450A3BJ = 135 UF
HF RC SNUBBERS 12 X (13.6 OHM 3 W + 1.1 NF) AND 10 X 47 NF TERMINAL CERAMICS
Cathode (2) to DC+, anode (1) to DC- at the bank terminals; terminal 3 unused. Reverse-biased in operation. Port short: carries 15.7 kA / 16.5 kA2s after the bank reverses (I2t 1.8 MA2s) instead of the module body diodes. CHASSIS-MOUNTED, insulated base plate (basic, to PE frame).
Switch 1/2 = leg A (AC1), 3/4 = leg B (AC2). Kelvin sources S1-S4 go to the drivers only (COM). NTC T1/T2 is read by the switch-2 driver (AIN referenced to S2), as on the CRD. Drains of 1/3 = DC+.
