vectivolt/PCM/hardware/DAB60/sheets/02_b1_gatea.kicad_sch

## KiCad design hardware/DAB60/sheets/02_b1_gatea.kicad_sch (2026-10-04)

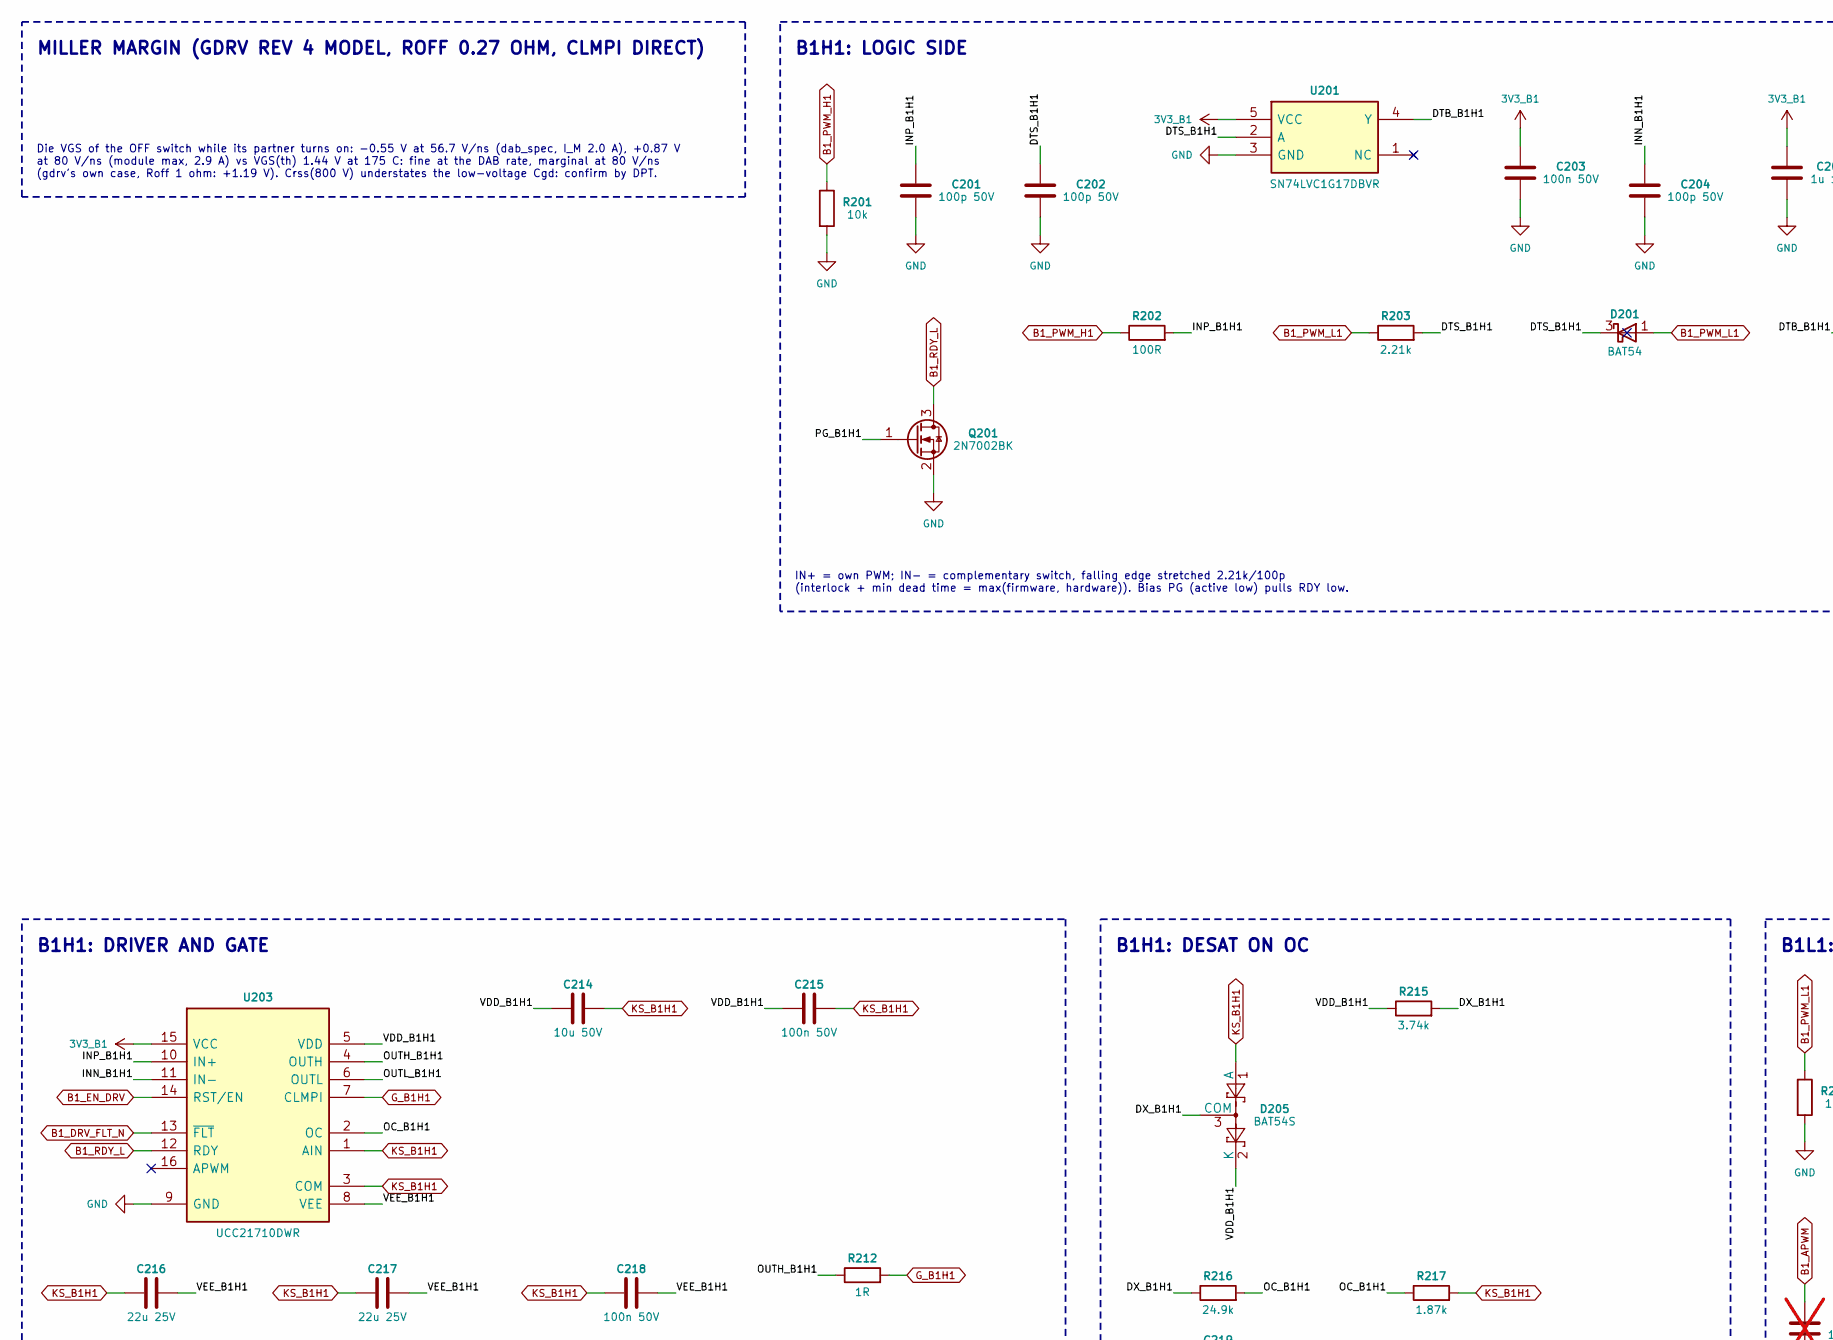
[picture p214: schematic 02_b1_gatea.kicad_sch, part in row 1, column 1]

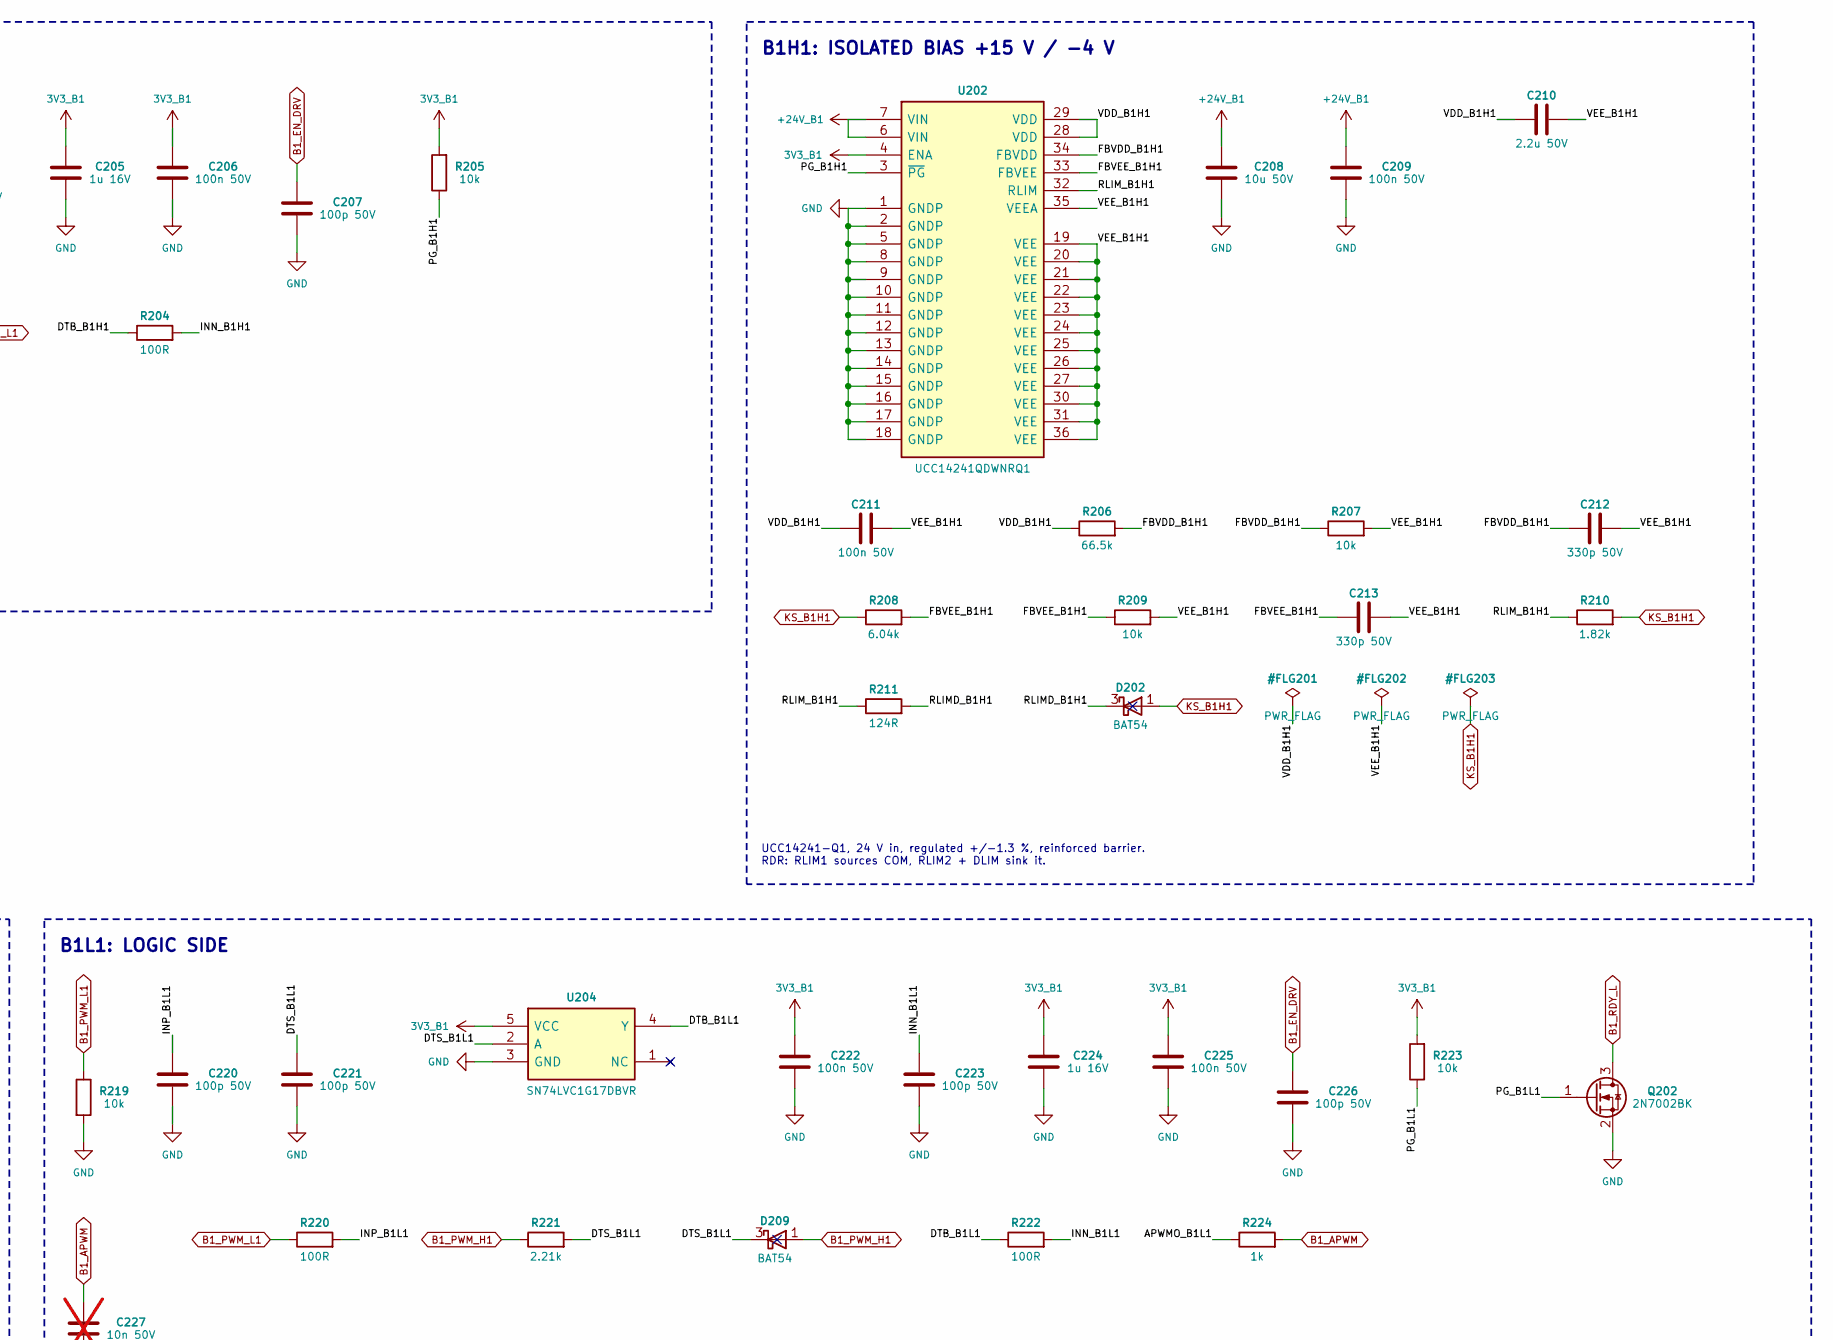
[picture p215: schematic 02_b1_gatea.kicad_sch, part in row 1, column 2]

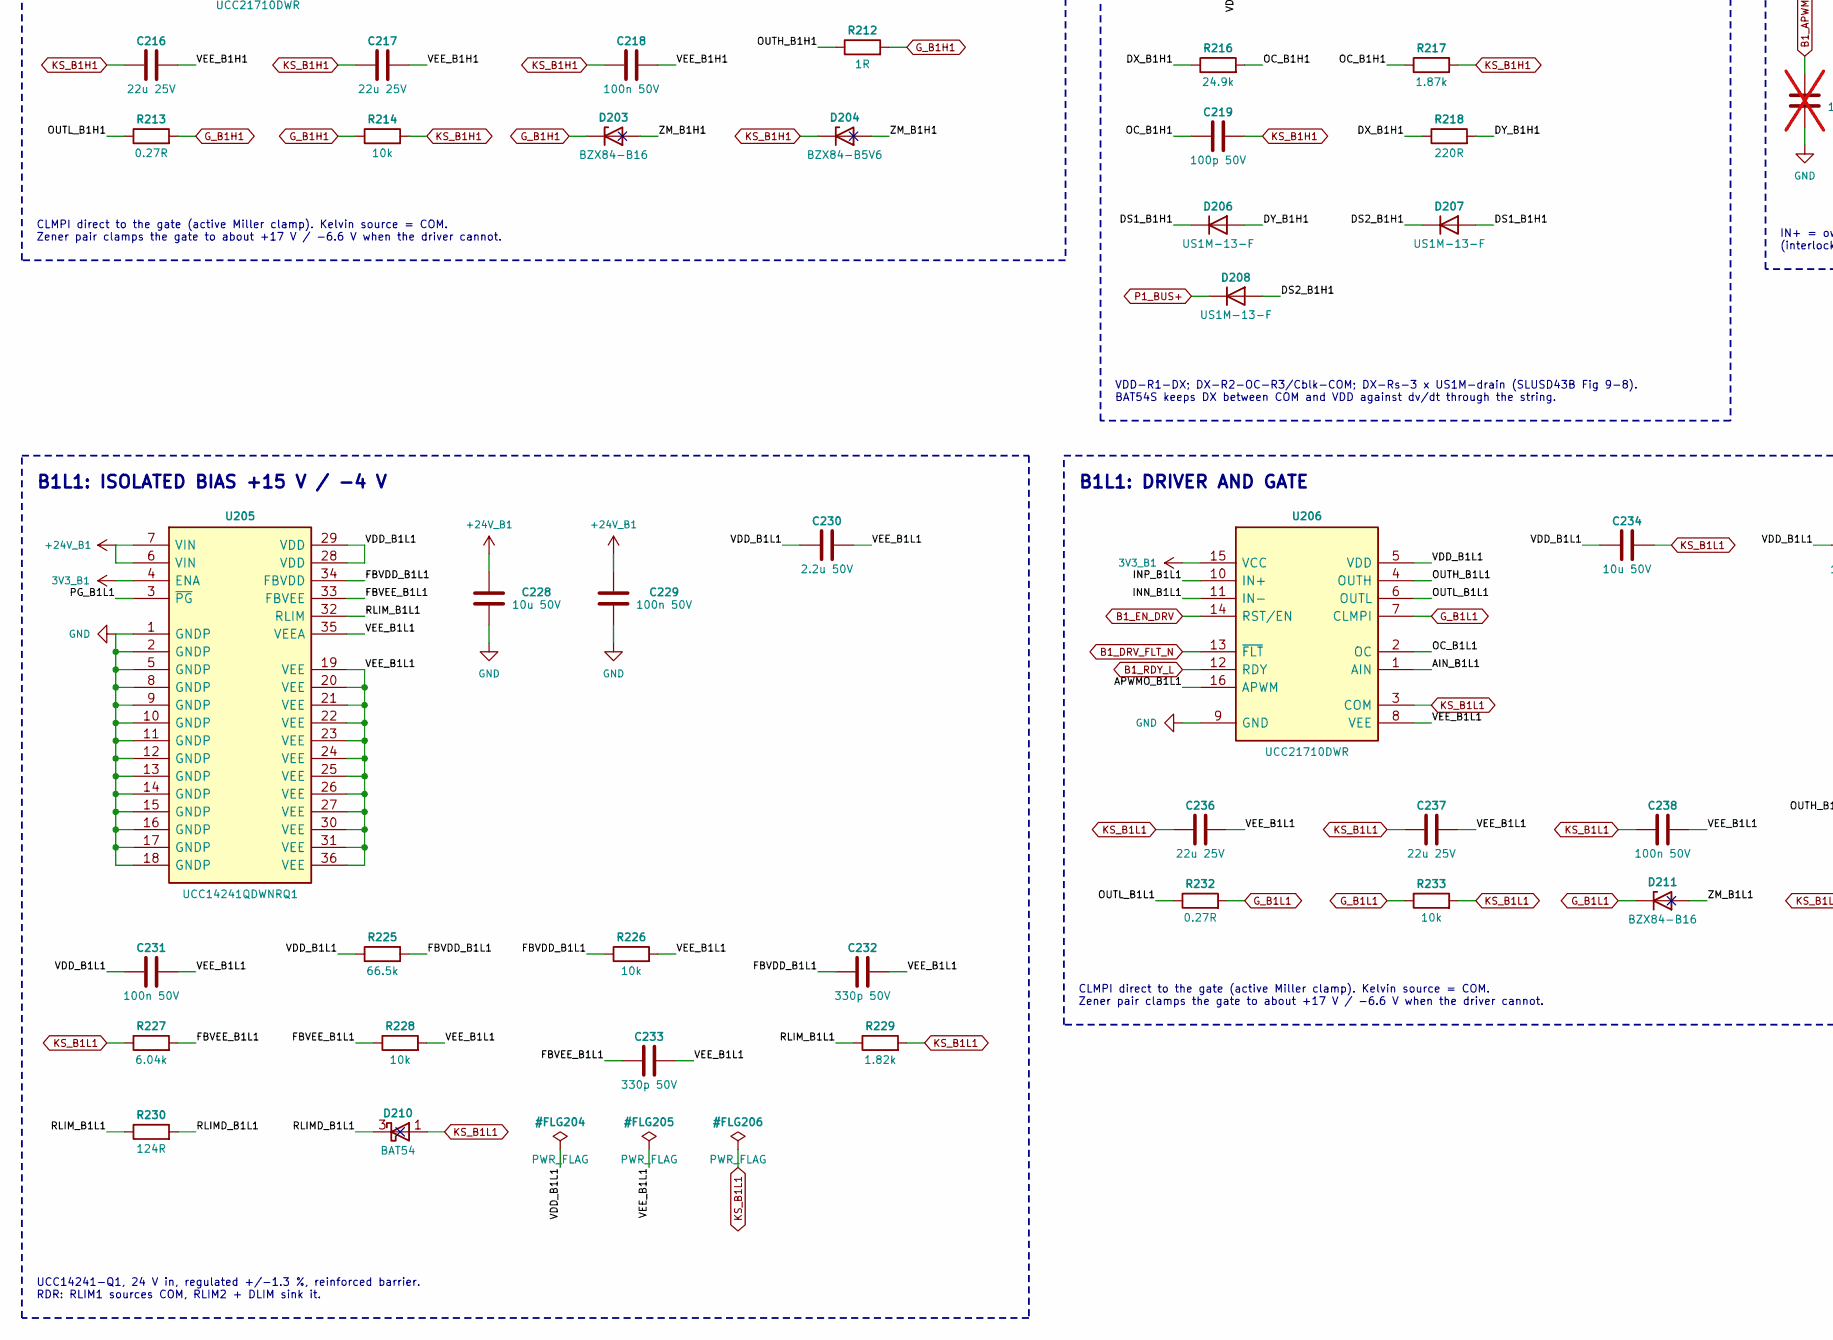
[picture p216: schematic 02_b1_gatea.kicad_sch, part in row 2, column 1]

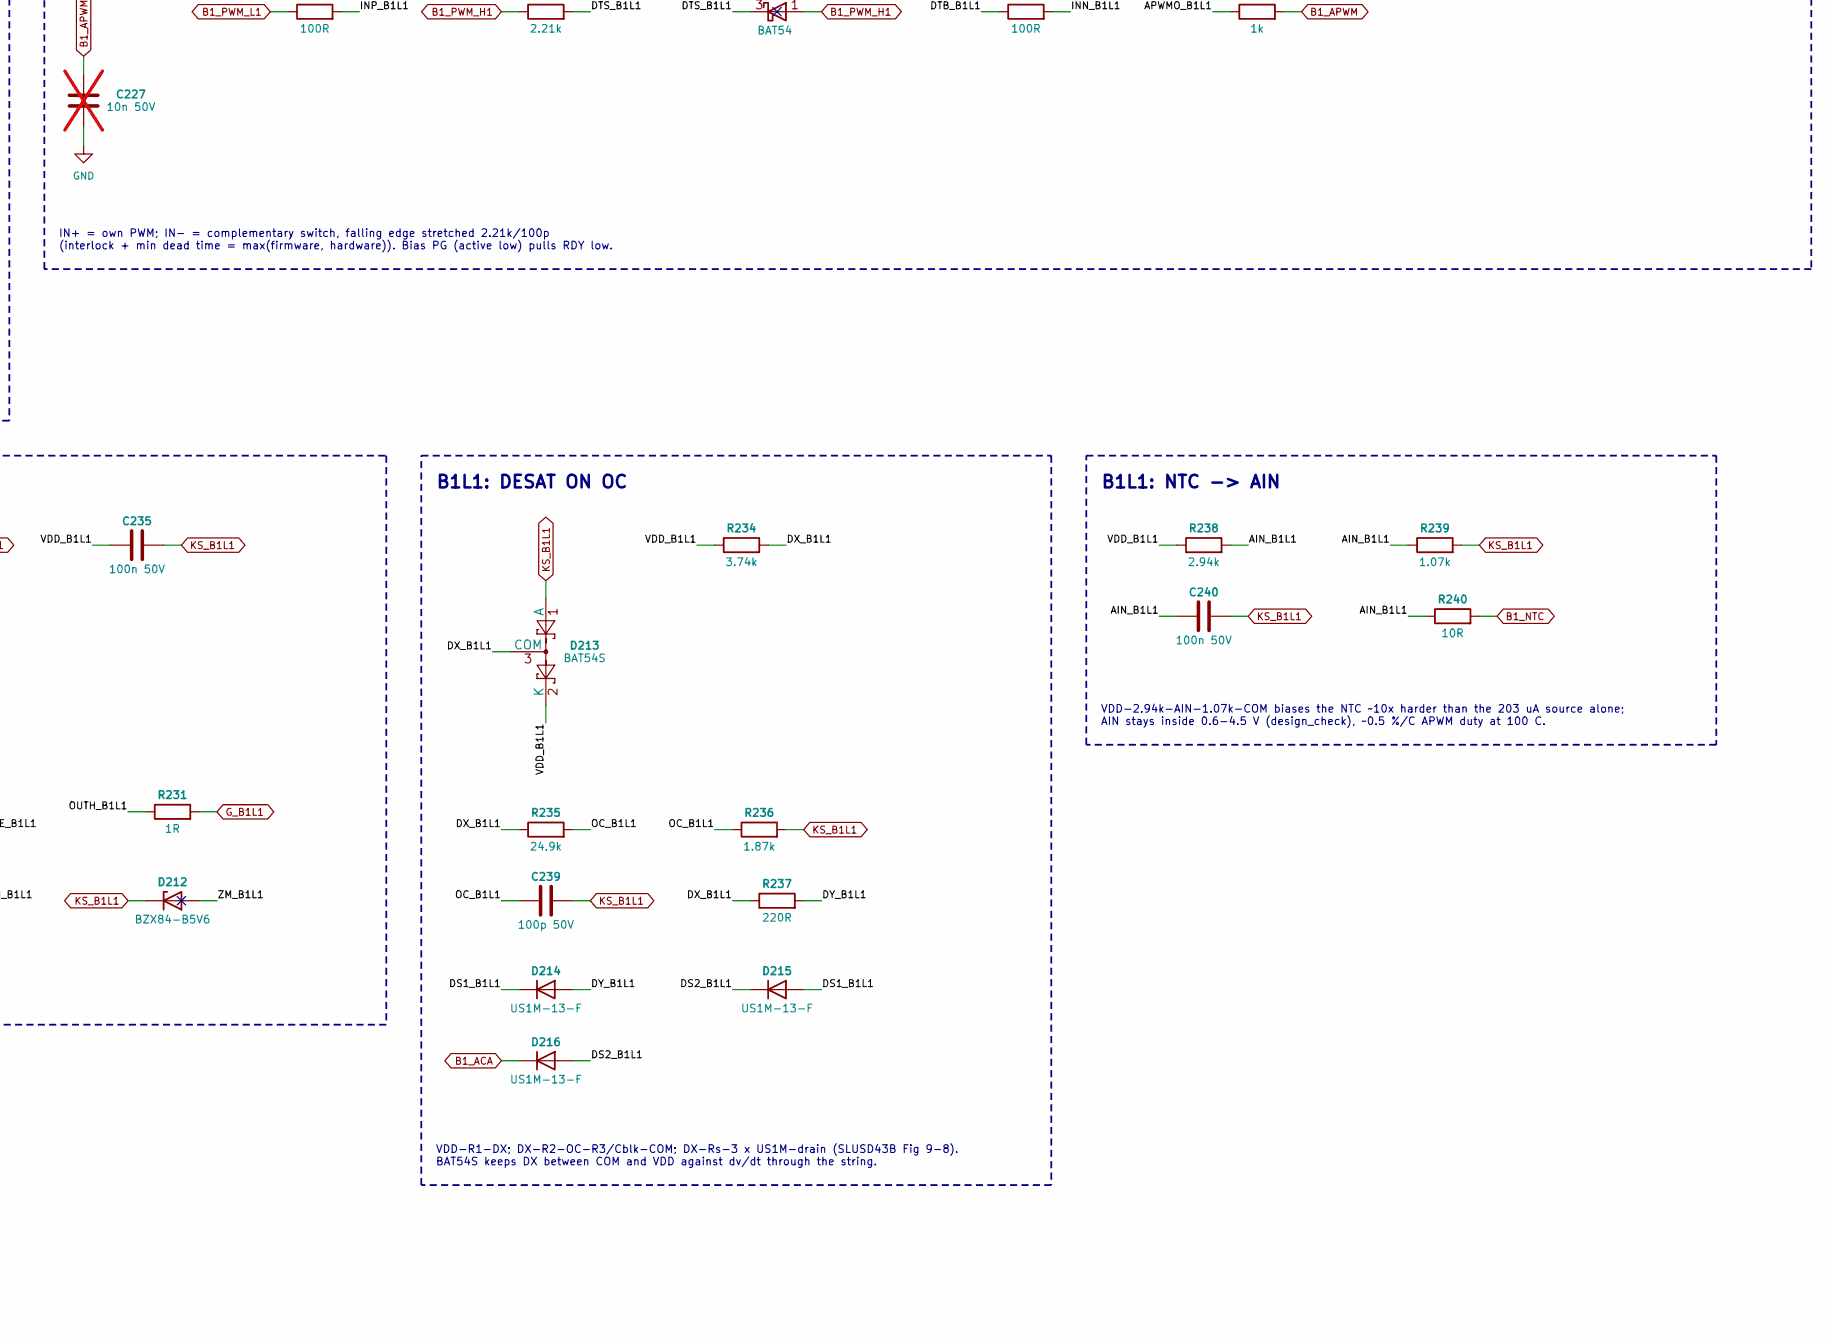
[picture p217: schematic 02_b1_gatea.kicad_sch, part in row 2, column 2]

Parts:
C201, C202, C204, C207, C219, C220, C221, C223, C226, C239: 100p 50V
C203, C206, C209, C211, C215, C218, C222, C225, C229, C231, C235, C238, C240: 100n 50V
C205, C224: 1u 16V
C208, C214, C228, C234: 10u 50V
C210, C230: 2.2u 50V
C212, C213, C232, C233: 330p 50V
C216, C217, C236, C237: 22u 25V
C227: 10n 50V; not fitted
D201, D202, D209, D210: BAT54; MPN BAT54
D203, D211: BZX84-B16; MPN BZX84-B16
D204, D212: BZX84-B5V6; MPN BZX84-B5V6
D205, D213: BAT54S; MPN BAT54S
D206, D207, D208, D214, D215, D216: US1M-13-F; MPN US1M-13-F
Q201, Q202: 2N7002BK; MPN 2N7002BK
R201, R205, R207, R209, R214, R219, R223, R226, R228, R233: 10k
R202, R204, R220, R222: 100R
R203, R221: 2.21k
R206, R225: 66.5k
R208, R227: 6.04k
R210, R229: 1.82k
R211, R230: 124R
R212, R231: 1R
R213, R232: 0.27R
R215, R234: 3.74k
R216, R235: 24.9k
R217, R236: 1.87k
R218, R237: 220R
R224: 1k
R238: 2.94k
R239: 1.07k
R240: 10R
U201, U204: SN74LVC1G17DBVR; MPN SN74LVC1G17DBVR
U202, U205: UCC14241QDWNRQ1; MPN UCC14241QDWNRQ1
U203, U206: UCC21710DWR; MPN UCC21710DWR

Connections:
3V3_B1: C203.1, C205.1, C206.1, C222.1, C224.1, C225.1, R205.2, R223.2, U201.5 (VCC), U202.4 (ENA), U203.15 (VCC), U204.5 (VCC), U205.4 (ENA), U206.15 (VCC)
+24V_B1: C208.1, C209.1, C228.1, C229.1, U202.6 (VIN), U202.7 (VIN), U205.6 (VIN), U205.7 (VIN)
AIN_B1L1: C240.1, R238.2, R239.1, R240.1, U206.1 (AIN)
APWMO_B1L1: R224.1, U206.16 (APWM)
B1_ACA: D216.1 (K)
B1_APWM: C227.1, R224.2
B1_DRV_FLT_N: U203.13 (~FLT), U206.13 (~FLT)
B1_EN_DRV: C207.1, C226.1, U203.14 (RST/EN), U206.14 (RST/EN)
B1_NTC: R240.2
B1_PWM_H1: D209.1 (A), R201.1, R202.1, R221.1
B1_PWM_L1: D201.1 (A), R203.1, R219.1, R220.1
B1_RDY_L: Q201.3 (D), Q202.3 (D), U203.12 (RDY), U206.12 (RDY)
DS1_B1H1: D206.1 (K), D207.2 (A)
DS1_B1L1: D214.1 (K), D215.2 (A)
DS2_B1H1: D207.1 (K), D208.2 (A)
DS2_B1L1: D215.1 (K), D216.2 (A)
DTB_B1H1: R204.1, U201.4 (Y)
DTB_B1L1: R222.1, U204.4 (Y)
DTS_B1H1: C202.1, D201.3 (K), R203.2, U201.2 (A)
DTS_B1L1: C221.1, D209.3 (K), R221.2, U204.2 (A)
DX_B1H1: D205.3 (COM), R215.2, R216.1, R218.1
DX_B1L1: D213.3 (COM), R234.2, R235.1, R237.1
DY_B1H1: D206.2 (A), R218.2
DY_B1L1: D214.2 (A), R237.2
FBVDD_B1H1: C212.1, R206.2, R207.1, U202.34 (FBVDD)
FBVDD_B1L1: C232.1, R225.2, R226.1, U205.34 (FBVDD)
FBVEE_B1H1: C213.1, R208.2, R209.1, U202.33 (FBVEE)
FBVEE_B1L1: C233.1, R227.2, R228.1, U205.33 (FBVEE)
GND: C201.2, C202.2, C203.2, C204.2, C205.2, C206.2, C207.2, C208.2, C209.2, C220.2, C221.2, C222.2, C223.2, C224.2, C225.2, C226.2, C227.2, C228.2, C229.2, Q201.2 (S), Q202.2 (S), R201.2, R219.2, U201.3 (GND), U202.1 (GNDP), U202.2 (GNDP), U202.5 (GNDP), U202.8 (GNDP), U202.9 (GNDP), U202.10 (GNDP), U202.11 (GNDP), U202.12 (GNDP), U202.13 (GNDP), U202.14 (GNDP), U202.15 (GNDP), U202.16 (GNDP), U202.17 (GNDP), U202.18 (GNDP), U203.9 (GND), U204.3 (GND), U205.1 (GNDP), U205.2 (GNDP), U205.5 (GNDP), U205.8 (GNDP), U205.9 (GNDP), U205.10 (GNDP), U205.11 (GNDP), U205.12 (GNDP), U205.13 (GNDP), U205.14 (GNDP), U205.15 (GNDP), U205.16 (GNDP), U205.17 (GNDP), U205.18 (GNDP), U206.9 (GND)
G_B1H1: D203.3 (K), R212.2, R213.2, R214.1, U203.7 (CLMPI)
G_B1L1: D211.3 (K), R231.2, R232.2, R233.1, U206.7 (CLMPI)
INN_B1H1: C204.1, R204.2, U203.11 (IN-)
INN_B1L1: C223.1, R222.2, U206.11 (IN-)
INP_B1H1: C201.1, R202.2, U203.10 (IN+)
INP_B1L1: C220.1, R220.2, U206.10 (IN+)
KS_B1H1: C214.2, C215.2, C216.1, C217.1, C218.1, C219.2, D202.1 (A), D204.3 (K), D205.1 (A), R208.1, R210.2, R214.2, R217.2, U203.1 (AIN), U203.3 (COM)
KS_B1L1: C234.2, C235.2, C236.1, C237.1, C238.1, C239.2, C240.2, D210.1 (A), D212.3 (K), D213.1 (A), R227.1, R229.2, R233.2, R236.2, R239.2, U206.3 (COM)
OC_B1H1: C219.1, R216.2, R217.1, U203.2 (OC)
OC_B1L1: C239.1, R235.2, R236.1, U206.2 (OC)
OUTH_B1H1: R212.1, U203.4 (OUTH)
OUTH_B1L1: R231.1, U206.4 (OUTH)
OUTL_B1H1: R213.1, U203.6 (OUTL)
OUTL_B1L1: R232.1, U206.6 (OUTL)
P1_BUS+: D208.1 (K)
PG_B1H1: Q201.1 (G), R205.1, U202.3 (~PG)
PG_B1L1: Q202.1 (G), R223.1, U205.3 (~PG)
RLIMD_B1H1: D202.3 (K), R211.2
RLIMD_B1L1: D210.3 (K), R230.2
RLIM_B1H1: R210.1, R211.1, U202.32 (RLIM)
RLIM_B1L1: R229.1, R230.1, U205.32 (RLIM)
VDD_B1H1: C210.1, C211.1, C214.1, C215.1, D205.2 (K), R206.1, R215.1, U202.28 (VDD), U202.29 (VDD), U203.5 (VDD)
VDD_B1L1: C230.1, C231.1, C234.1, C235.1, D213.2 (K), R225.1, R234.1, R238.1, U205.28 (VDD), U205.29 (VDD), U206.5 (VDD)
VEE_B1H1: C210.2, C211.2, C212.2, C213.2, C216.2, C217.2, C218.2, R207.2, R209.2, U202.19 (VEE), U202.20 (VEE), U202.21 (VEE), U202.22 (VEE), U202.23 (VEE), U202.24 (VEE), U202.25 (VEE), U202.26 (VEE), U202.27 (VEE), U202.30 (VEE), U202.31 (VEE), U202.35 (VEEA), U202.36 (VEE), U203.8 (VEE)
VEE_B1L1: C230.2, C231.2, C232.2, C233.2, C236.2, C237.2, C238.2, R226.2, R228.2, U205.19 (VEE), U205.20 (VEE), U205.21 (VEE), U205.22 (VEE), U205.23 (VEE), U205.24 (VEE), U205.25 (VEE), U205.26 (VEE), U205.27 (VEE), U205.30 (VEE), U205.31 (VEE), U205.35 (VEEA), U205.36 (VEE), U206.8 (VEE)
ZM_B1H1: D203.1 (A), D204.1 (A)
ZM_B1L1: D211.1 (A), D212.1 (A)

Notes on the sheet:
B1L1: NTC -> AIN
B1L1: LOGIC SIDE
Die VGS of the OFF switch while its partner turns on: -0.55 V at 56.7 V/ns (dab_spec, I_M 2.0 A), +0.87 V at 80 V/ns (module max, 2.9 A) vs VGS(th) 1.44 V at 175 C: fine at the DAB rate, marginal at 80 V/ns (gdrv's own case, Roff 1 ohm: +1.19 V). Crss(800 V) understates the low-voltage Cgd: confirm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
B1L1: DESAT ON OC
IN+ = own PWM; IN- = complementary switch, falling edge stretched 2.21k/100p (interlock + min dead time = max(firmware, hardware)). Bias PG (active low) pulls RDY low.
VDD-R1-DX; DX-R2-OC-R3/Cblk-COM; DX-Rs-3 x US1M-drain (SLUSD43B Fig 9-8). BAT54S keeps DX between COM and VDD against dv/dt through the string.
B1L1: ISOLATED BIAS +15 V / -4 V
CLMPI direct to the gate (active Miller clamp). Kelvin source = COM. Zener pair clamps the gate to about +17 V / -6.6 V when the driver cannot.
B1H1: LOGIC SIDE
B1H1: DRIVER AND GATE
B1H1: ISOLATED BIAS +15 V / -4 V
VDD-2.94k-AIN-1.07k-COM biases the NTC ~10x harder than the 203 uA source alone; AIN stays inside 0.6-4.5 V (design_check), ~0.5 %/C APWM duty at 100 C.
UCC14241-Q1, 24 V in, regulated +/-1.3 %, reinforced barrier. RDR: RLIM1 sources COM, RLIM2 + DLIM sink it.
B1H1: DESAT ON OC
B1L1: DRIVER AND GATE
MILLER MARGIN (GDRV REV 4 MODEL, ROFF 0.27 OHM, CLMPI DIRECT)
