vectivolt/PCM/hardware/DAB60/sheets/03_b1_gateb.kicad_sch

## KiCad design hardware/DAB60/sheets/03_b1_gateb.kicad_sch (2026-10-04)

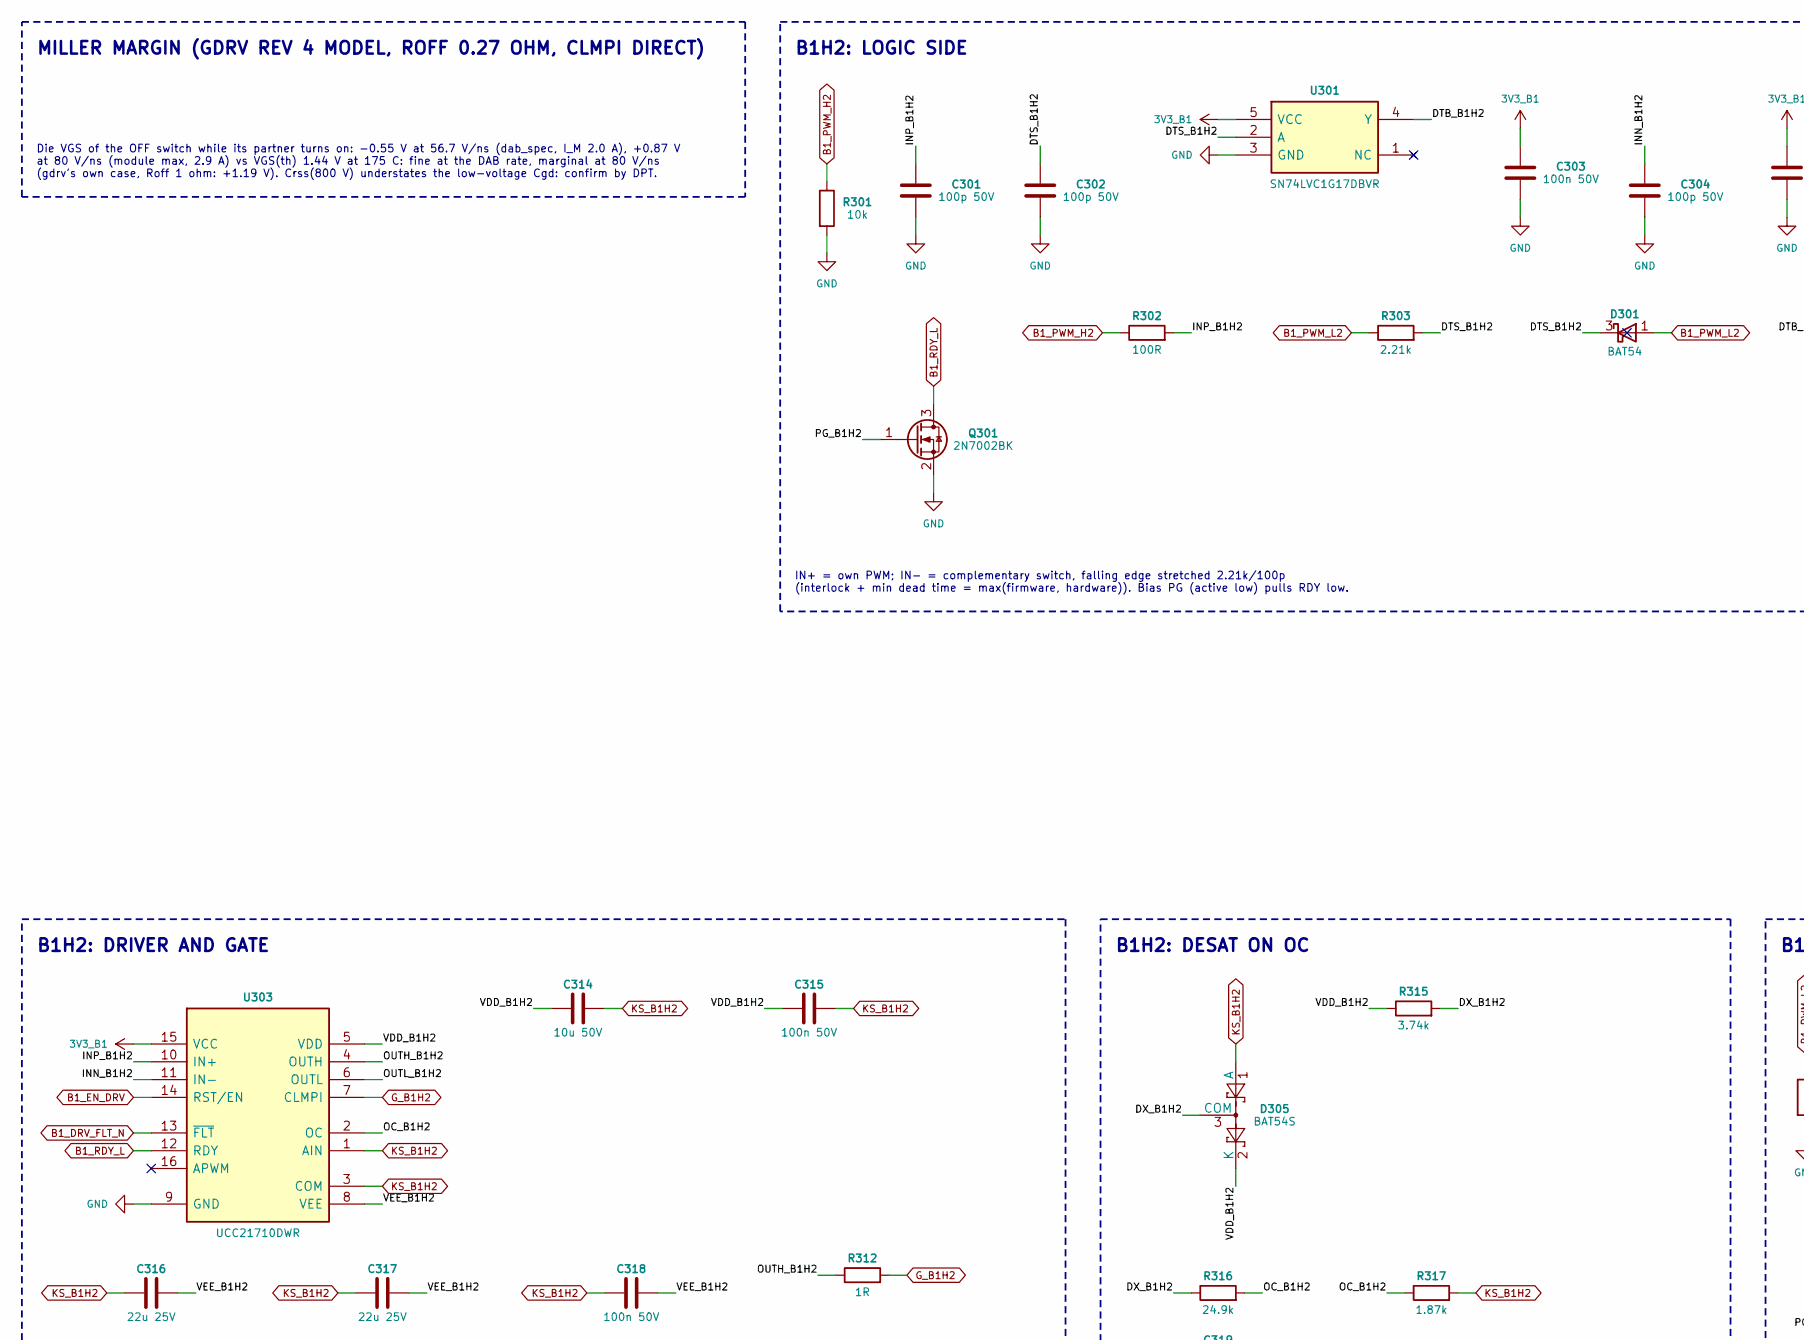
[picture p218: schematic 03_b1_gateb.kicad_sch, part in row 1, column 1]

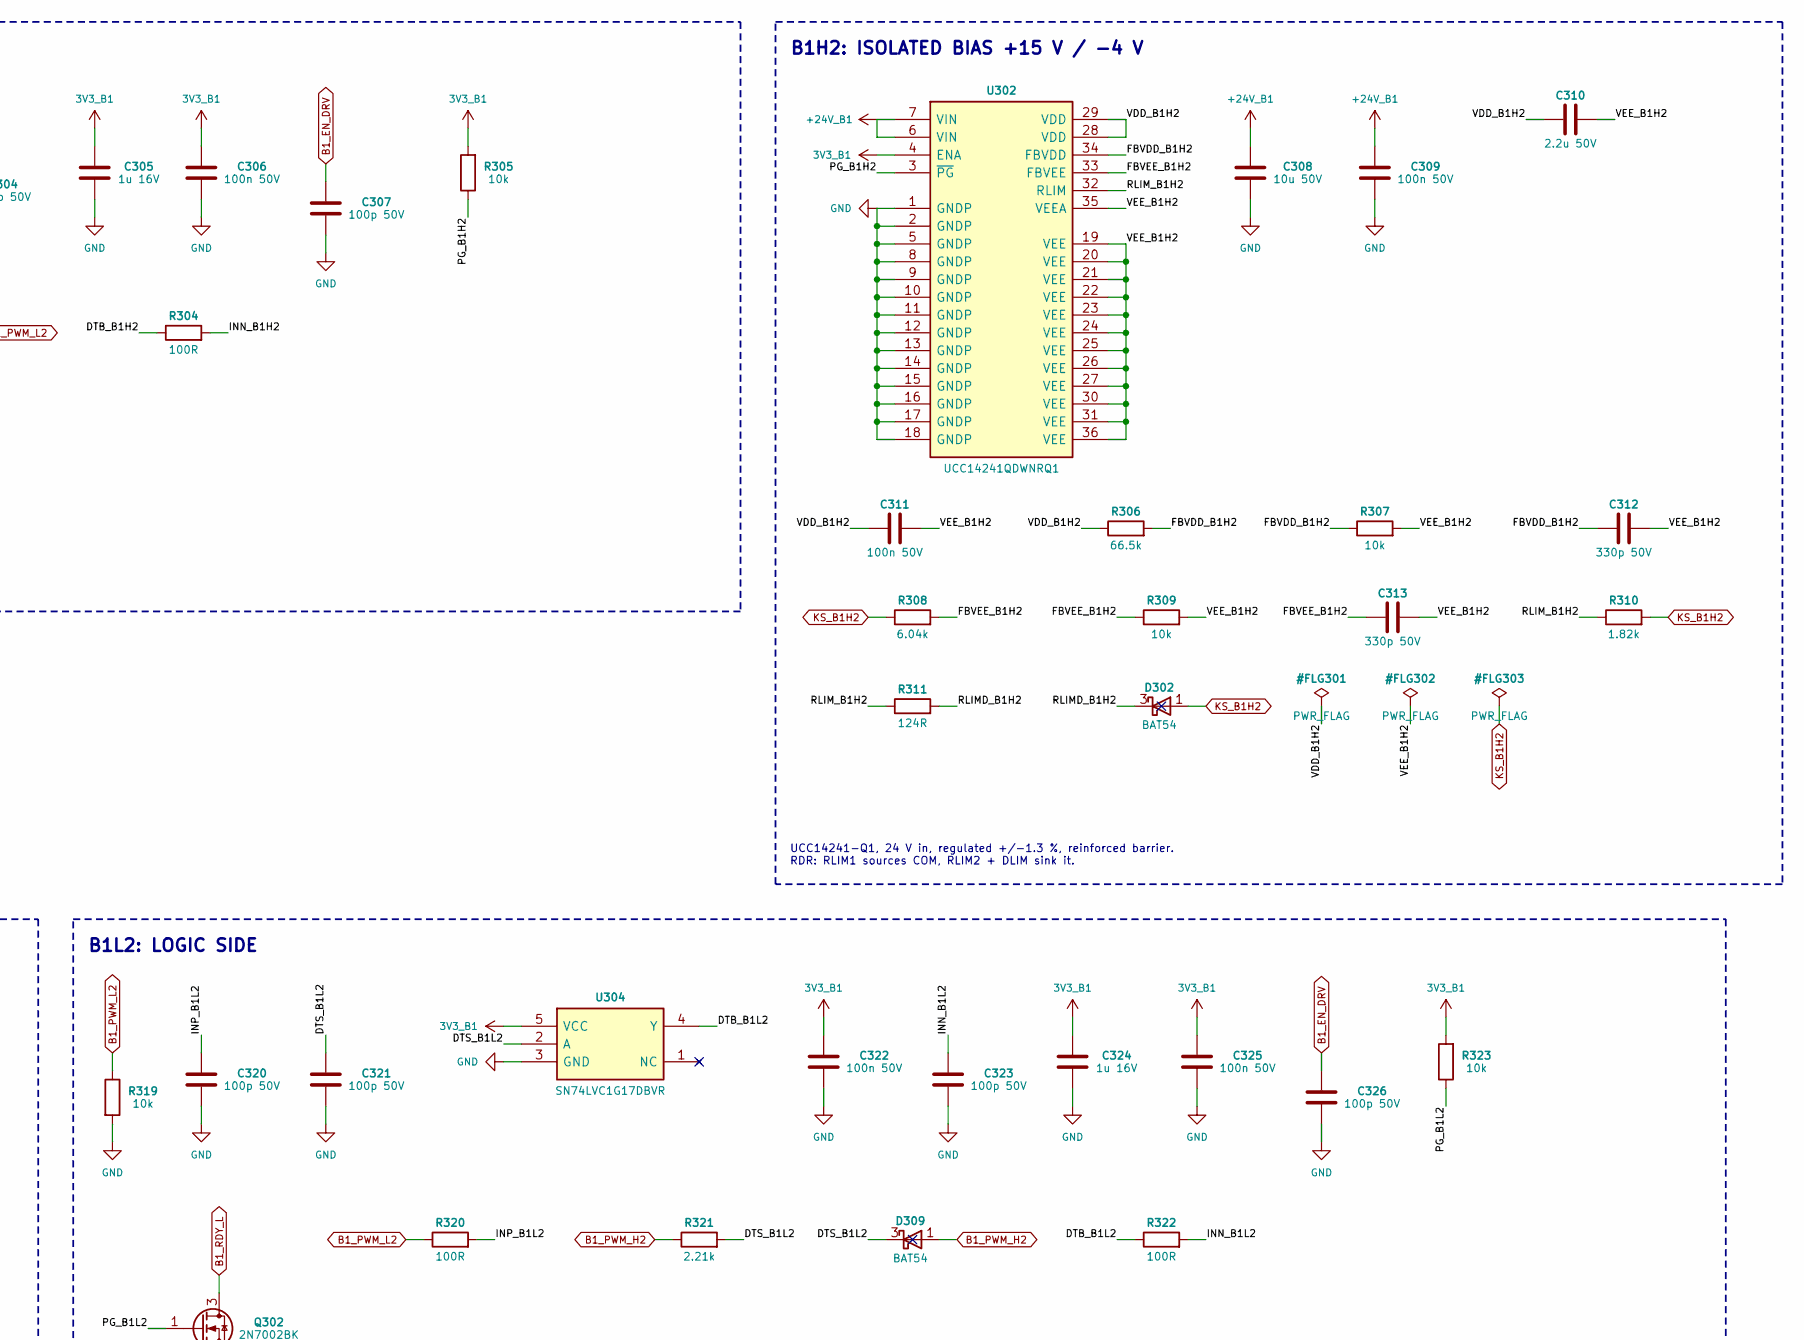
[picture p219: schematic 03_b1_gateb.kicad_sch, part in row 1, column 2]

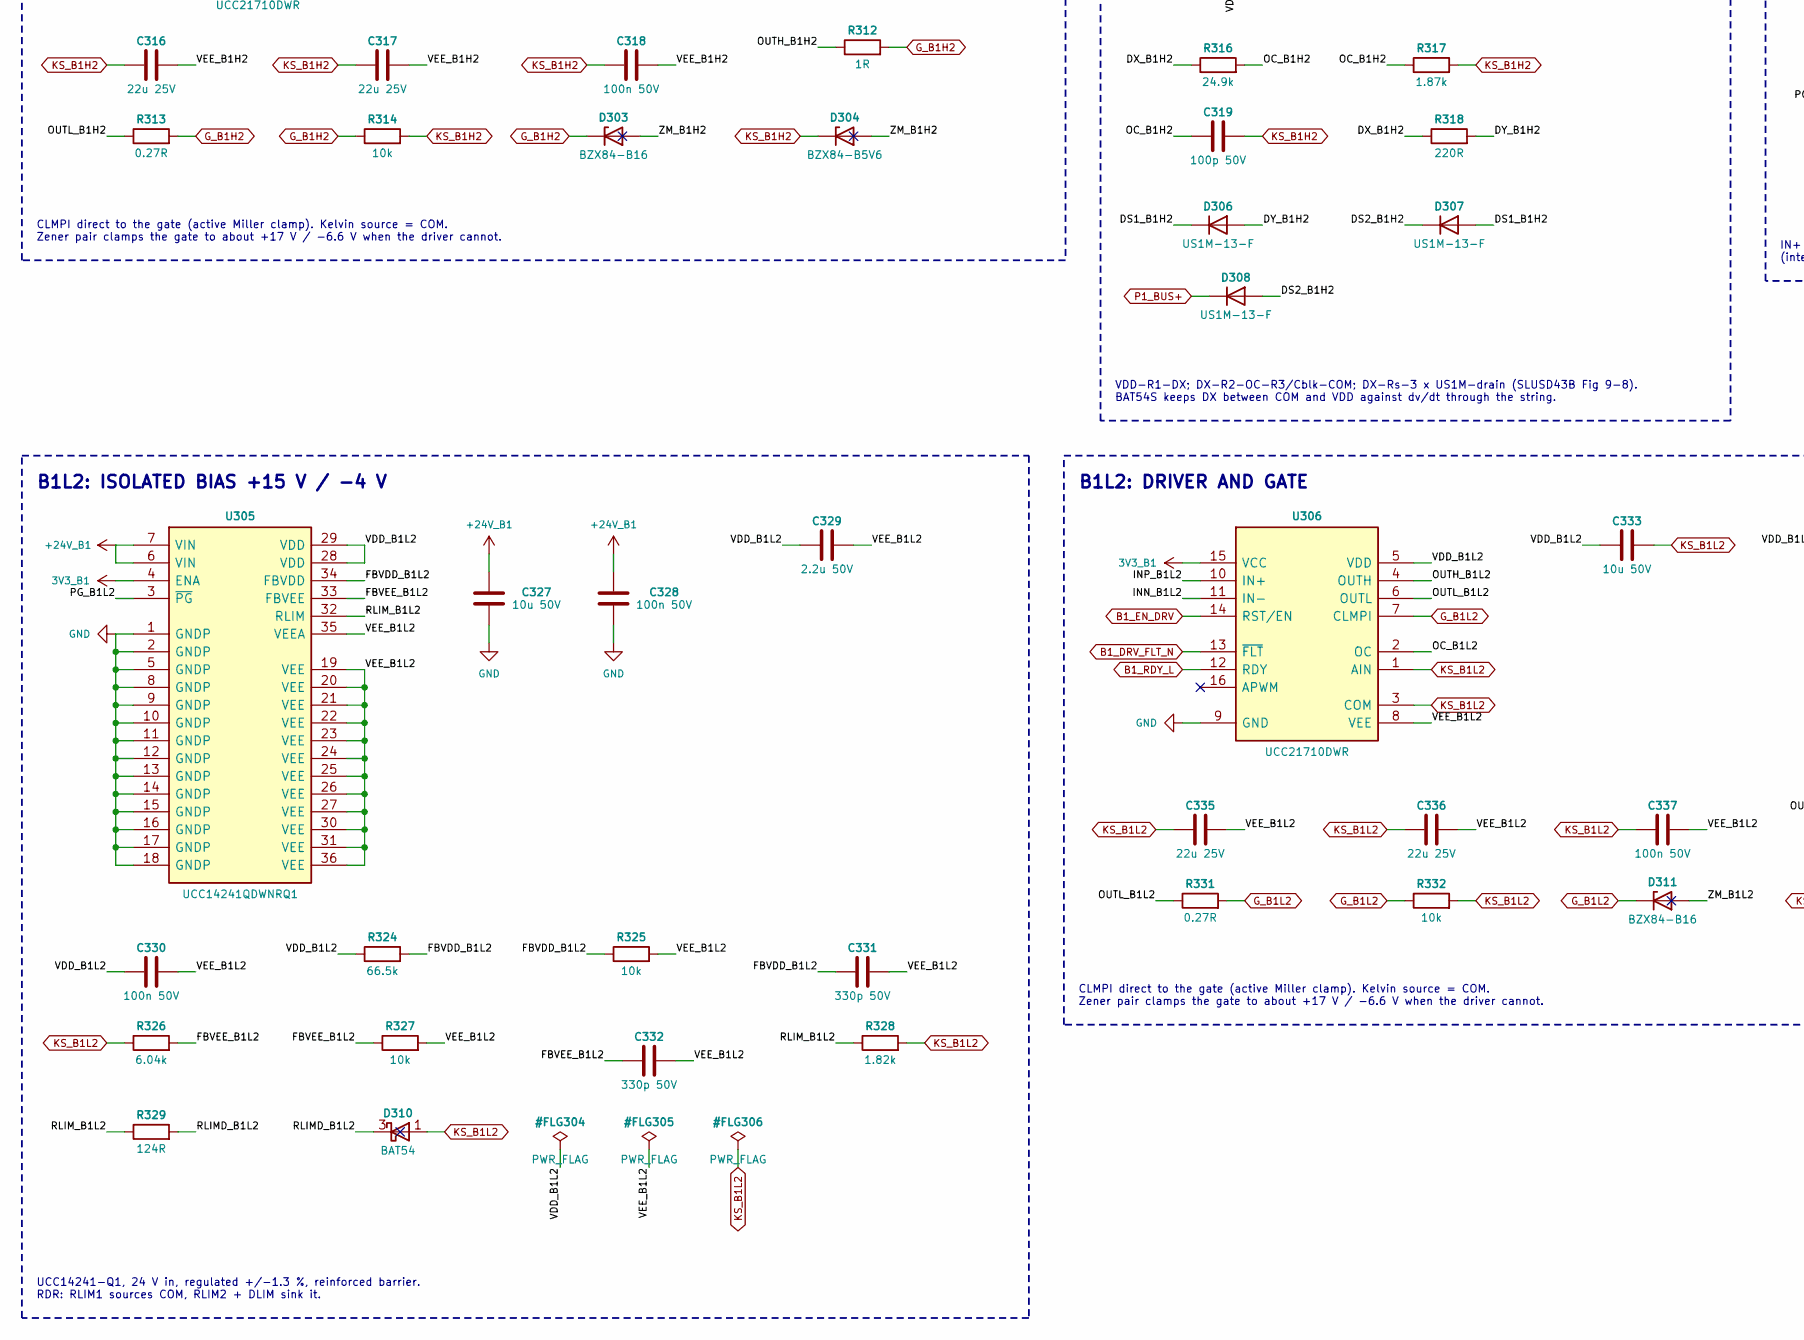
[picture p220: schematic 03_b1_gateb.kicad_sch, part in row 2, column 1]

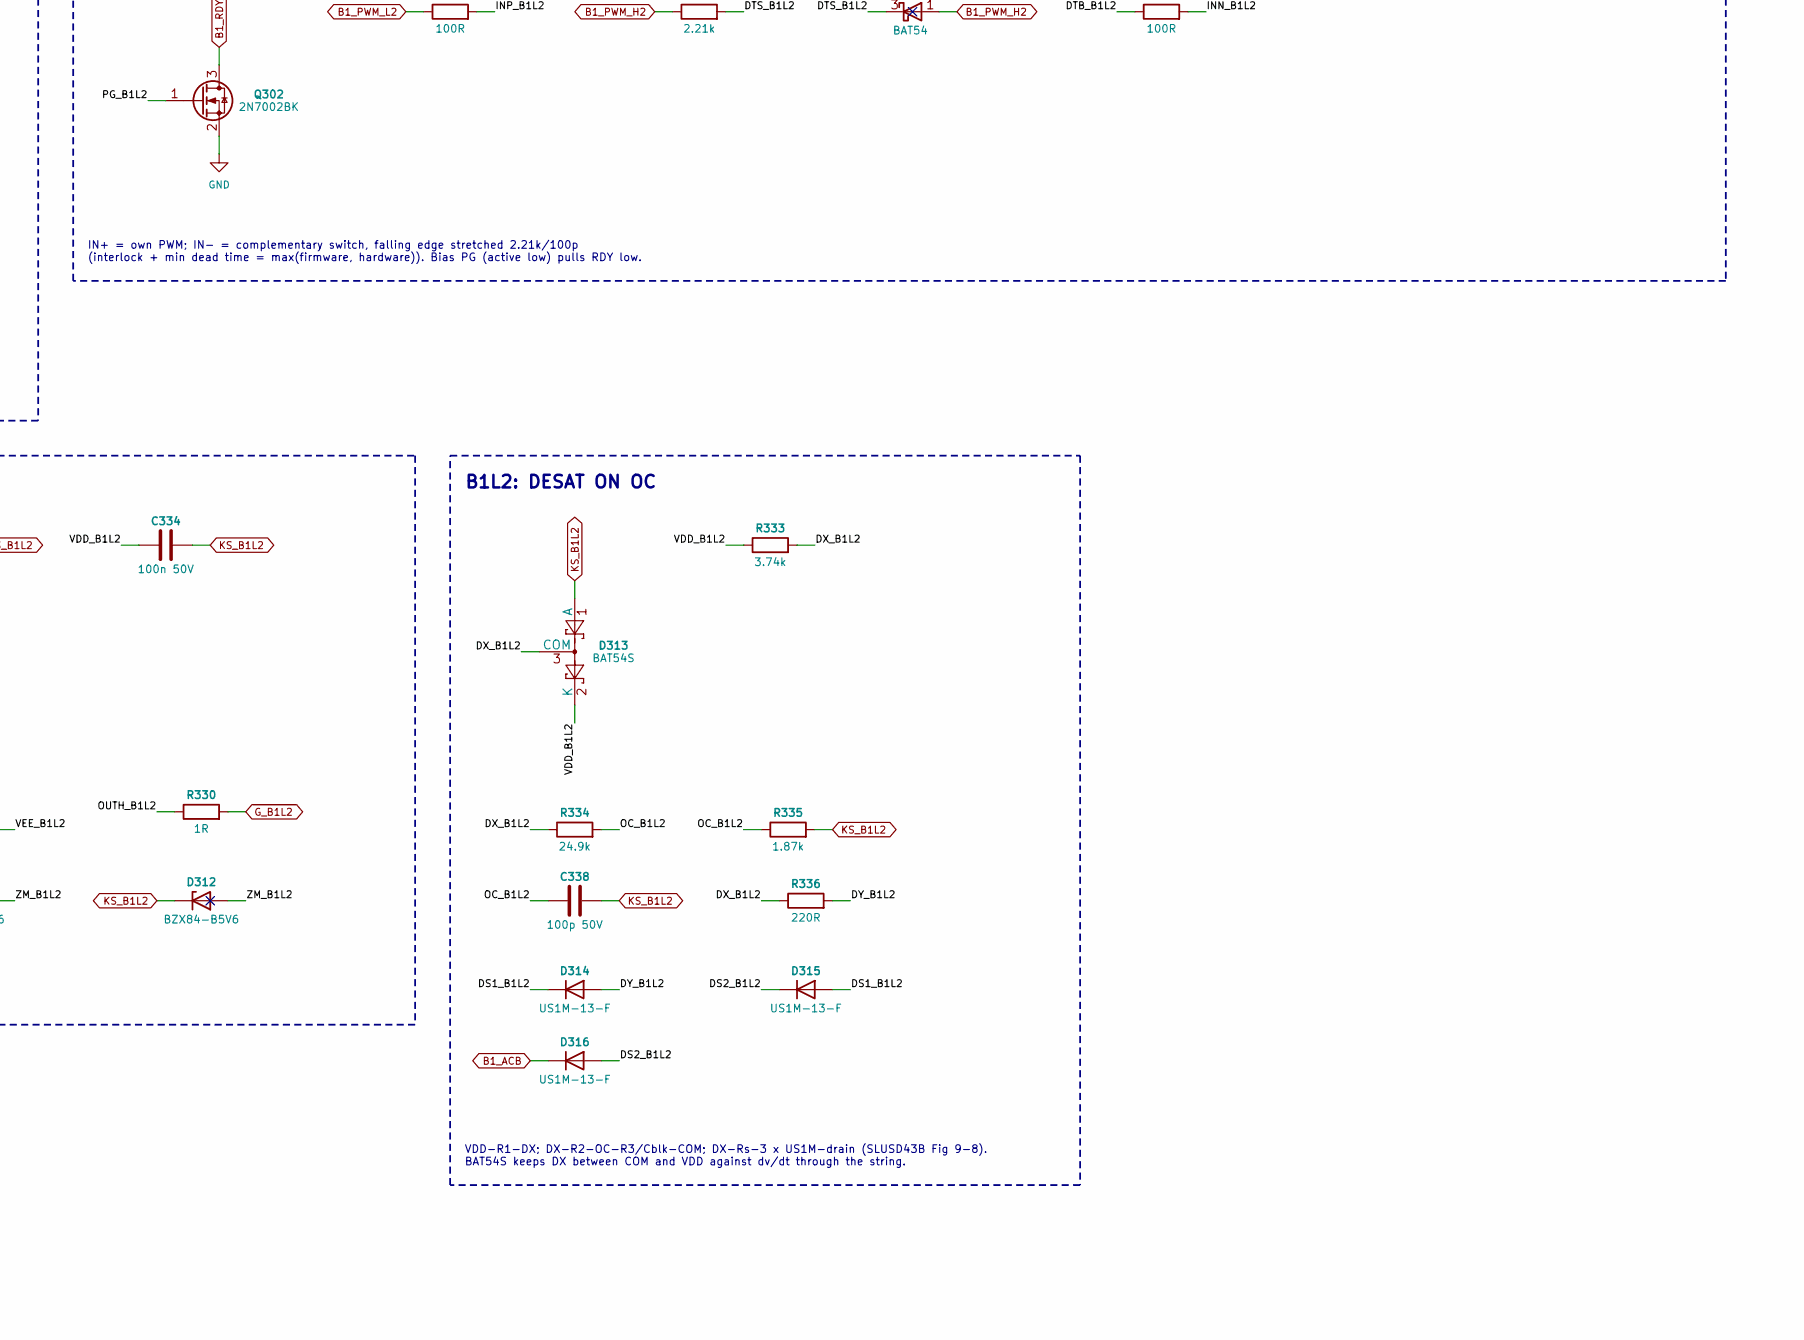
[picture p221: schematic 03_b1_gateb.kicad_sch, part in row 2, column 2]

Parts:
C301, C302, C304, C307, C319, C320, C321, C323, C326, C338: 100p 50V
C303, C306, C309, C311, C315, C318, C322, C325, C328, C330, C334, C337: 100n 50V
C305, C324: 1u 16V
C308, C314, C327, C333: 10u 50V
C310, C329: 2.2u 50V
C312, C313, C331, C332: 330p 50V
C316, C317, C335, C336: 22u 25V
D301, D302, D309, D310: BAT54; MPN BAT54
D303, D311: BZX84-B16; MPN BZX84-B16
D304, D312: BZX84-B5V6; MPN BZX84-B5V6
D305, D313: BAT54S; MPN BAT54S
D306, D307, D308, D314, D315, D316: US1M-13-F; MPN US1M-13-F
Q301, Q302: 2N7002BK; MPN 2N7002BK
R301, R305, R307, R309, R314, R319, R323, R325, R327, R332: 10k
R302, R304, R320, R322: 100R
R303, R321: 2.21k
R306, R324: 66.5k
R308, R326: 6.04k
R310, R328: 1.82k
R311, R329: 124R
R312, R330: 1R
R313, R331: 0.27R
R315, R333: 3.74k
R316, R334: 24.9k
R317, R335: 1.87k
R318, R336: 220R
U301, U304: SN74LVC1G17DBVR; MPN SN74LVC1G17DBVR
U302, U305: UCC14241QDWNRQ1; MPN UCC14241QDWNRQ1
U303, U306: UCC21710DWR; MPN UCC21710DWR

Connections:
3V3_B1: C303.1, C305.1, C306.1, C322.1, C324.1, C325.1, R305.2, R323.2, U301.5 (VCC), U302.4 (ENA), U303.15 (VCC), U304.5 (VCC), U305.4 (ENA), U306.15 (VCC)
+24V_B1: C308.1, C309.1, C327.1, C328.1, U302.6 (VIN), U302.7 (VIN), U305.6 (VIN), U305.7 (VIN)
B1_ACB: D316.1 (K)
B1_DRV_FLT_N: U303.13 (~FLT), U306.13 (~FLT)
B1_EN_DRV: C307.1, C326.1, U303.14 (RST/EN), U306.14 (RST/EN)
B1_PWM_H2: D309.1 (A), R301.1, R302.1, R321.1
B1_PWM_L2: D301.1 (A), R303.1, R319.1, R320.1
B1_RDY_L: Q301.3 (D), Q302.3 (D), U303.12 (RDY), U306.12 (RDY)
DS1_B1H2: D306.1 (K), D307.2 (A)
DS1_B1L2: D314.1 (K), D315.2 (A)
DS2_B1H2: D307.1 (K), D308.2 (A)
DS2_B1L2: D315.1 (K), D316.2 (A)
DTB_B1H2: R304.1, U301.4 (Y)
DTB_B1L2: R322.1, U304.4 (Y)
DTS_B1H2: C302.1, D301.3 (K), R303.2, U301.2 (A)
DTS_B1L2: C321.1, D309.3 (K), R321.2, U304.2 (A)
DX_B1H2: D305.3 (COM), R315.2, R316.1, R318.1
DX_B1L2: D313.3 (COM), R333.2, R334.1, R336.1
DY_B1H2: D306.2 (A), R318.2
DY_B1L2: D314.2 (A), R336.2
FBVDD_B1H2: C312.1, R306.2, R307.1, U302.34 (FBVDD)
FBVDD_B1L2: C331.1, R324.2, R325.1, U305.34 (FBVDD)
FBVEE_B1H2: C313.1, R308.2, R309.1, U302.33 (FBVEE)
FBVEE_B1L2: C332.1, R326.2, R327.1, U305.33 (FBVEE)
GND: C301.2, C302.2, C303.2, C304.2, C305.2, C306.2, C307.2, C308.2, C309.2, C320.2, C321.2, C322.2, C323.2, C324.2, C325.2, C326.2, C327.2, C328.2, Q301.2 (S), Q302.2 (S), R301.2, R319.2, U301.3 (GND), U302.1 (GNDP), U302.2 (GNDP), U302.5 (GNDP), U302.8 (GNDP), U302.9 (GNDP), U302.10 (GNDP), U302.11 (GNDP), U302.12 (GNDP), U302.13 (GNDP), U302.14 (GNDP), U302.15 (GNDP), U302.16 (GNDP), U302.17 (GNDP), U302.18 (GNDP), U303.9 (GND), U304.3 (GND), U305.1 (GNDP), U305.2 (GNDP), U305.5 (GNDP), U305.8 (GNDP), U305.9 (GNDP), U305.10 (GNDP), U305.11 (GNDP), U305.12 (GNDP), U305.13 (GNDP), U305.14 (GNDP), U305.15 (GNDP), U305.16 (GNDP), U305.17 (GNDP), U305.18 (GNDP), U306.9 (GND)
G_B1H2: D303.3 (K), R312.2, R313.2, R314.1, U303.7 (CLMPI)
G_B1L2: D311.3 (K), R330.2, R331.2, R332.1, U306.7 (CLMPI)
INN_B1H2: C304.1, R304.2, U303.11 (IN-)
INN_B1L2: C323.1, R322.2, U306.11 (IN-)
INP_B1H2: C301.1, R302.2, U303.10 (IN+)
INP_B1L2: C320.1, R320.2, U306.10 (IN+)
KS_B1H2: C314.2, C315.2, C316.1, C317.1, C318.1, C319.2, D302.1 (A), D304.3 (K), D305.1 (A), R308.1, R310.2, R314.2, R317.2, U303.1 (AIN), U303.3 (COM)
KS_B1L2: C333.2, C334.2, C335.1, C336.1, C337.1, C338.2, D310.1 (A), D312.3 (K), D313.1 (A), R326.1, R328.2, R332.2, R335.2, U306.1 (AIN), U306.3 (COM)
OC_B1H2: C319.1, R316.2, R317.1, U303.2 (OC)
OC_B1L2: C338.1, R334.2, R335.1, U306.2 (OC)
OUTH_B1H2: R312.1, U303.4 (OUTH)
OUTH_B1L2: R330.1, U306.4 (OUTH)
OUTL_B1H2: R313.1, U303.6 (OUTL)
OUTL_B1L2: R331.1, U306.6 (OUTL)
P1_BUS+: D308.1 (K)
PG_B1H2: Q301.1 (G), R305.1, U302.3 (~PG)
PG_B1L2: Q302.1 (G), R323.1, U305.3 (~PG)
RLIMD_B1H2: D302.3 (K), R311.2
RLIMD_B1L2: D310.3 (K), R329.2
RLIM_B1H2: R310.1, R311.1, U302.32 (RLIM)
RLIM_B1L2: R328.1, R329.1, U305.32 (RLIM)
VDD_B1H2: C310.1, C311.1, C314.1, C315.1, D305.2 (K), R306.1, R315.1, U302.28 (VDD), U302.29 (VDD), U303.5 (VDD)
VDD_B1L2: C329.1, C330.1, C333.1, C334.1, D313.2 (K), R324.1, R333.1, U305.28 (VDD), U305.29 (VDD), U306.5 (VDD)
VEE_B1H2: C310.2, C311.2, C312.2, C313.2, C316.2, C317.2, C318.2, R307.2, R309.2, U302.19 (VEE), U302.20 (VEE), U302.21 (VEE), U302.22 (VEE), U302.23 (VEE), U302.24 (VEE), U302.25 (VEE), U302.26 (VEE), U302.27 (VEE), U302.30 (VEE), U302.31 (VEE), U302.35 (VEEA), U302.36 (VEE), U303.8 (VEE)
VEE_B1L2: C329.2, C330.2, C331.2, C332.2, C335.2, C336.2, C337.2, R325.2, R327.2, U305.19 (VEE), U305.20 (VEE), U305.21 (VEE), U305.22 (VEE), U305.23 (VEE), U305.24 (VEE), U305.25 (VEE), U305.26 (VEE), U305.27 (VEE), U305.30 (VEE), U305.31 (VEE), U305.35 (VEEA), U305.36 (VEE), U306.8 (VEE)
ZM_B1H2: D303.1 (A), D304.1 (A)
ZM_B1L2: D311.1 (A), D312.1 (A)

Notes on the sheet:
B1H2: DRIVER AND GATE
UCC14241-Q1, 24 V in, regulated +/-1.3 %, reinforced barrier. RDR: RLIM1 sources COM, RLIM2 + DLIM sink it.
B1H2: DESAT ON OC
CLMPI direct to the gate (active Miller clamp). Kelvin source = COM. Zener pair clamps the gate to about +17 V / -6.6 V when the driver cannot.
B1L2: DRIVER AND GATE
B1H2: ISOLATED BIAS +15 V / -4 V
Die VGS of the OFF switch while its partner turns on: -0.55 V at 56.7 V/ns (dab_spec, I_M 2.0 A), +0.87 V at 80 V/ns (module max, 2.9 A) vs VGS(th) 1.44 V at 175 C: fine at the DAB rate, marginal at 80 V/ns (gdrv's own case, Roff 1 ohm: +1.19 V). Crss(800 V) understates the low-voltage Cgd: confirm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
B1L2: ISOLATED BIAS +15 V / -4 V
B1L2: DESAT ON OC
IN+ = own PWM; IN- = complementary switch, falling edge stretched 2.21k/100p (interlock + min dead time = max(firmware, hardware)). Bias PG (active low) pulls RDY low.
VDD-R1-DX; DX-R2-OC-R3/Cblk-COM; DX-Rs-3 x US1M-drain (SLUSD43B Fig 9-8). BAT54S keeps DX between COM and VDD against dv/dt through the string.
B1H2: LOGIC SIDE
B1L2: LOGIC SIDE
MILLER MARGIN (GDRV REV 4 MODEL, ROFF 0.27 OHM, CLMPI DIRECT)
