vectivolt/PCM/hardware/DAB60/sheets/04_b1_if.kicad_sch

## KiCad design hardware/DAB60/sheets/04_b1_if.kicad_sch (2026-10-04)

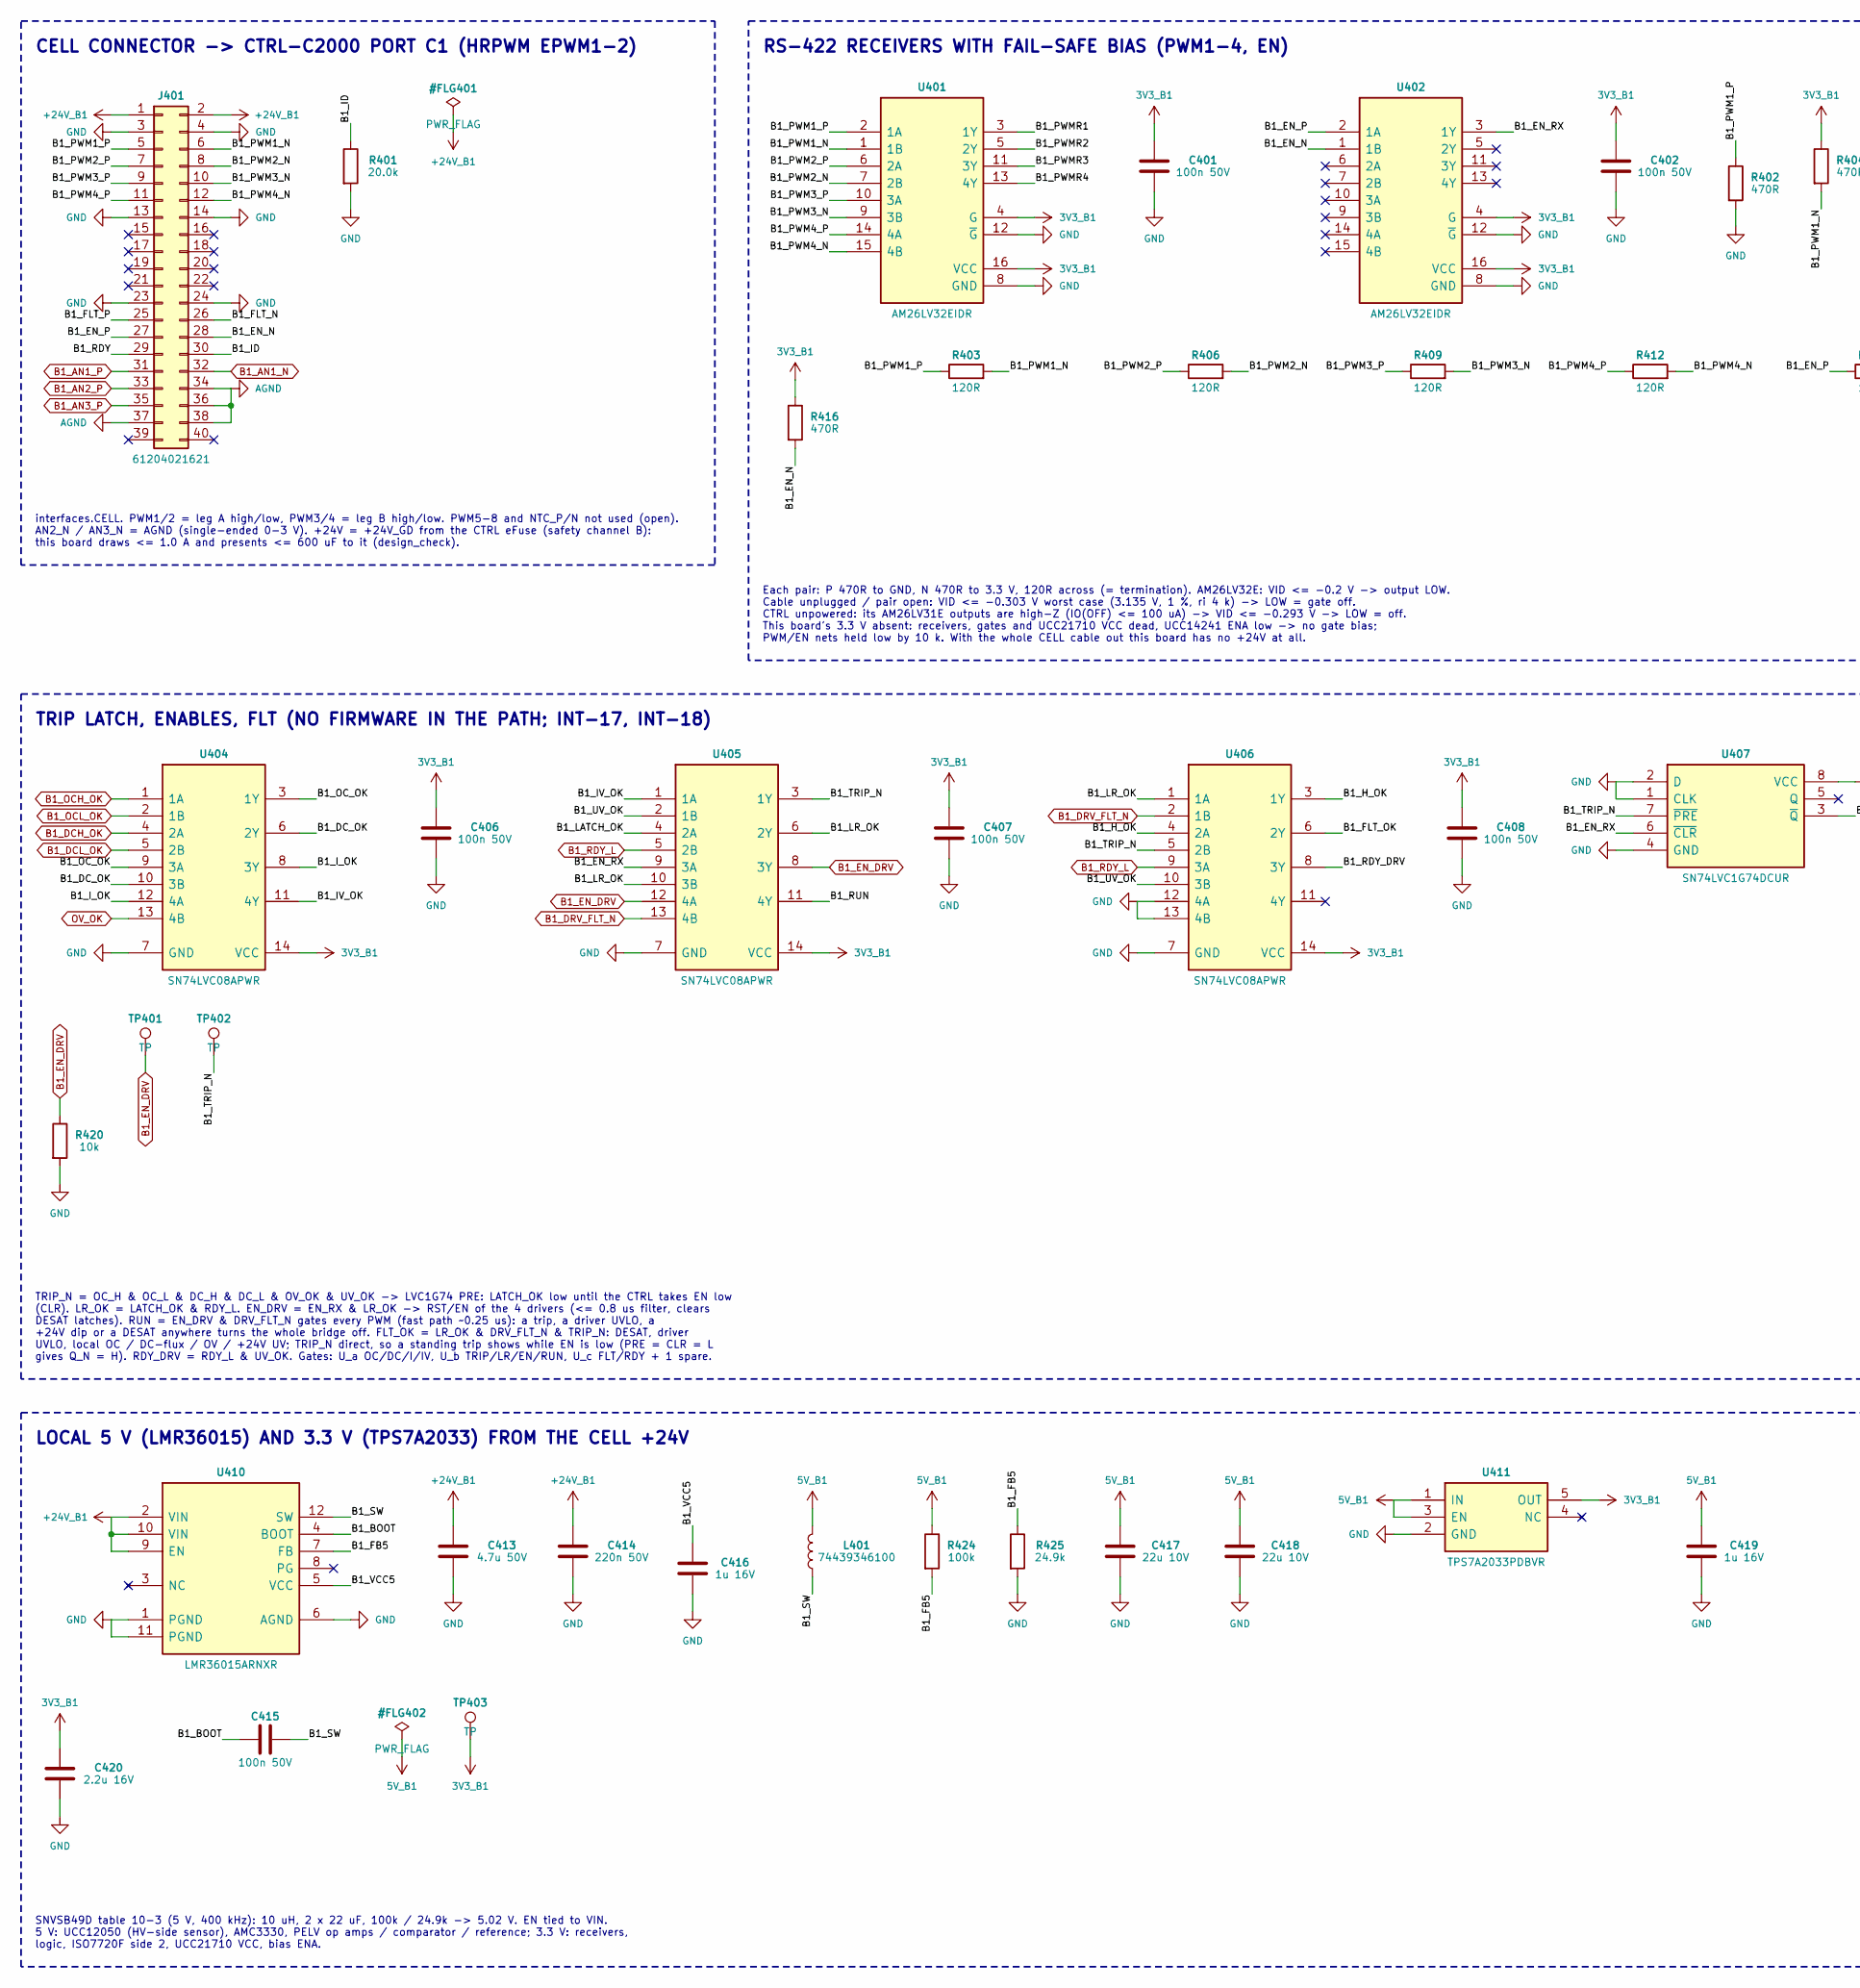
[picture p222: schematic 04_b1_if.kicad_sch, part in row 1, column 1]

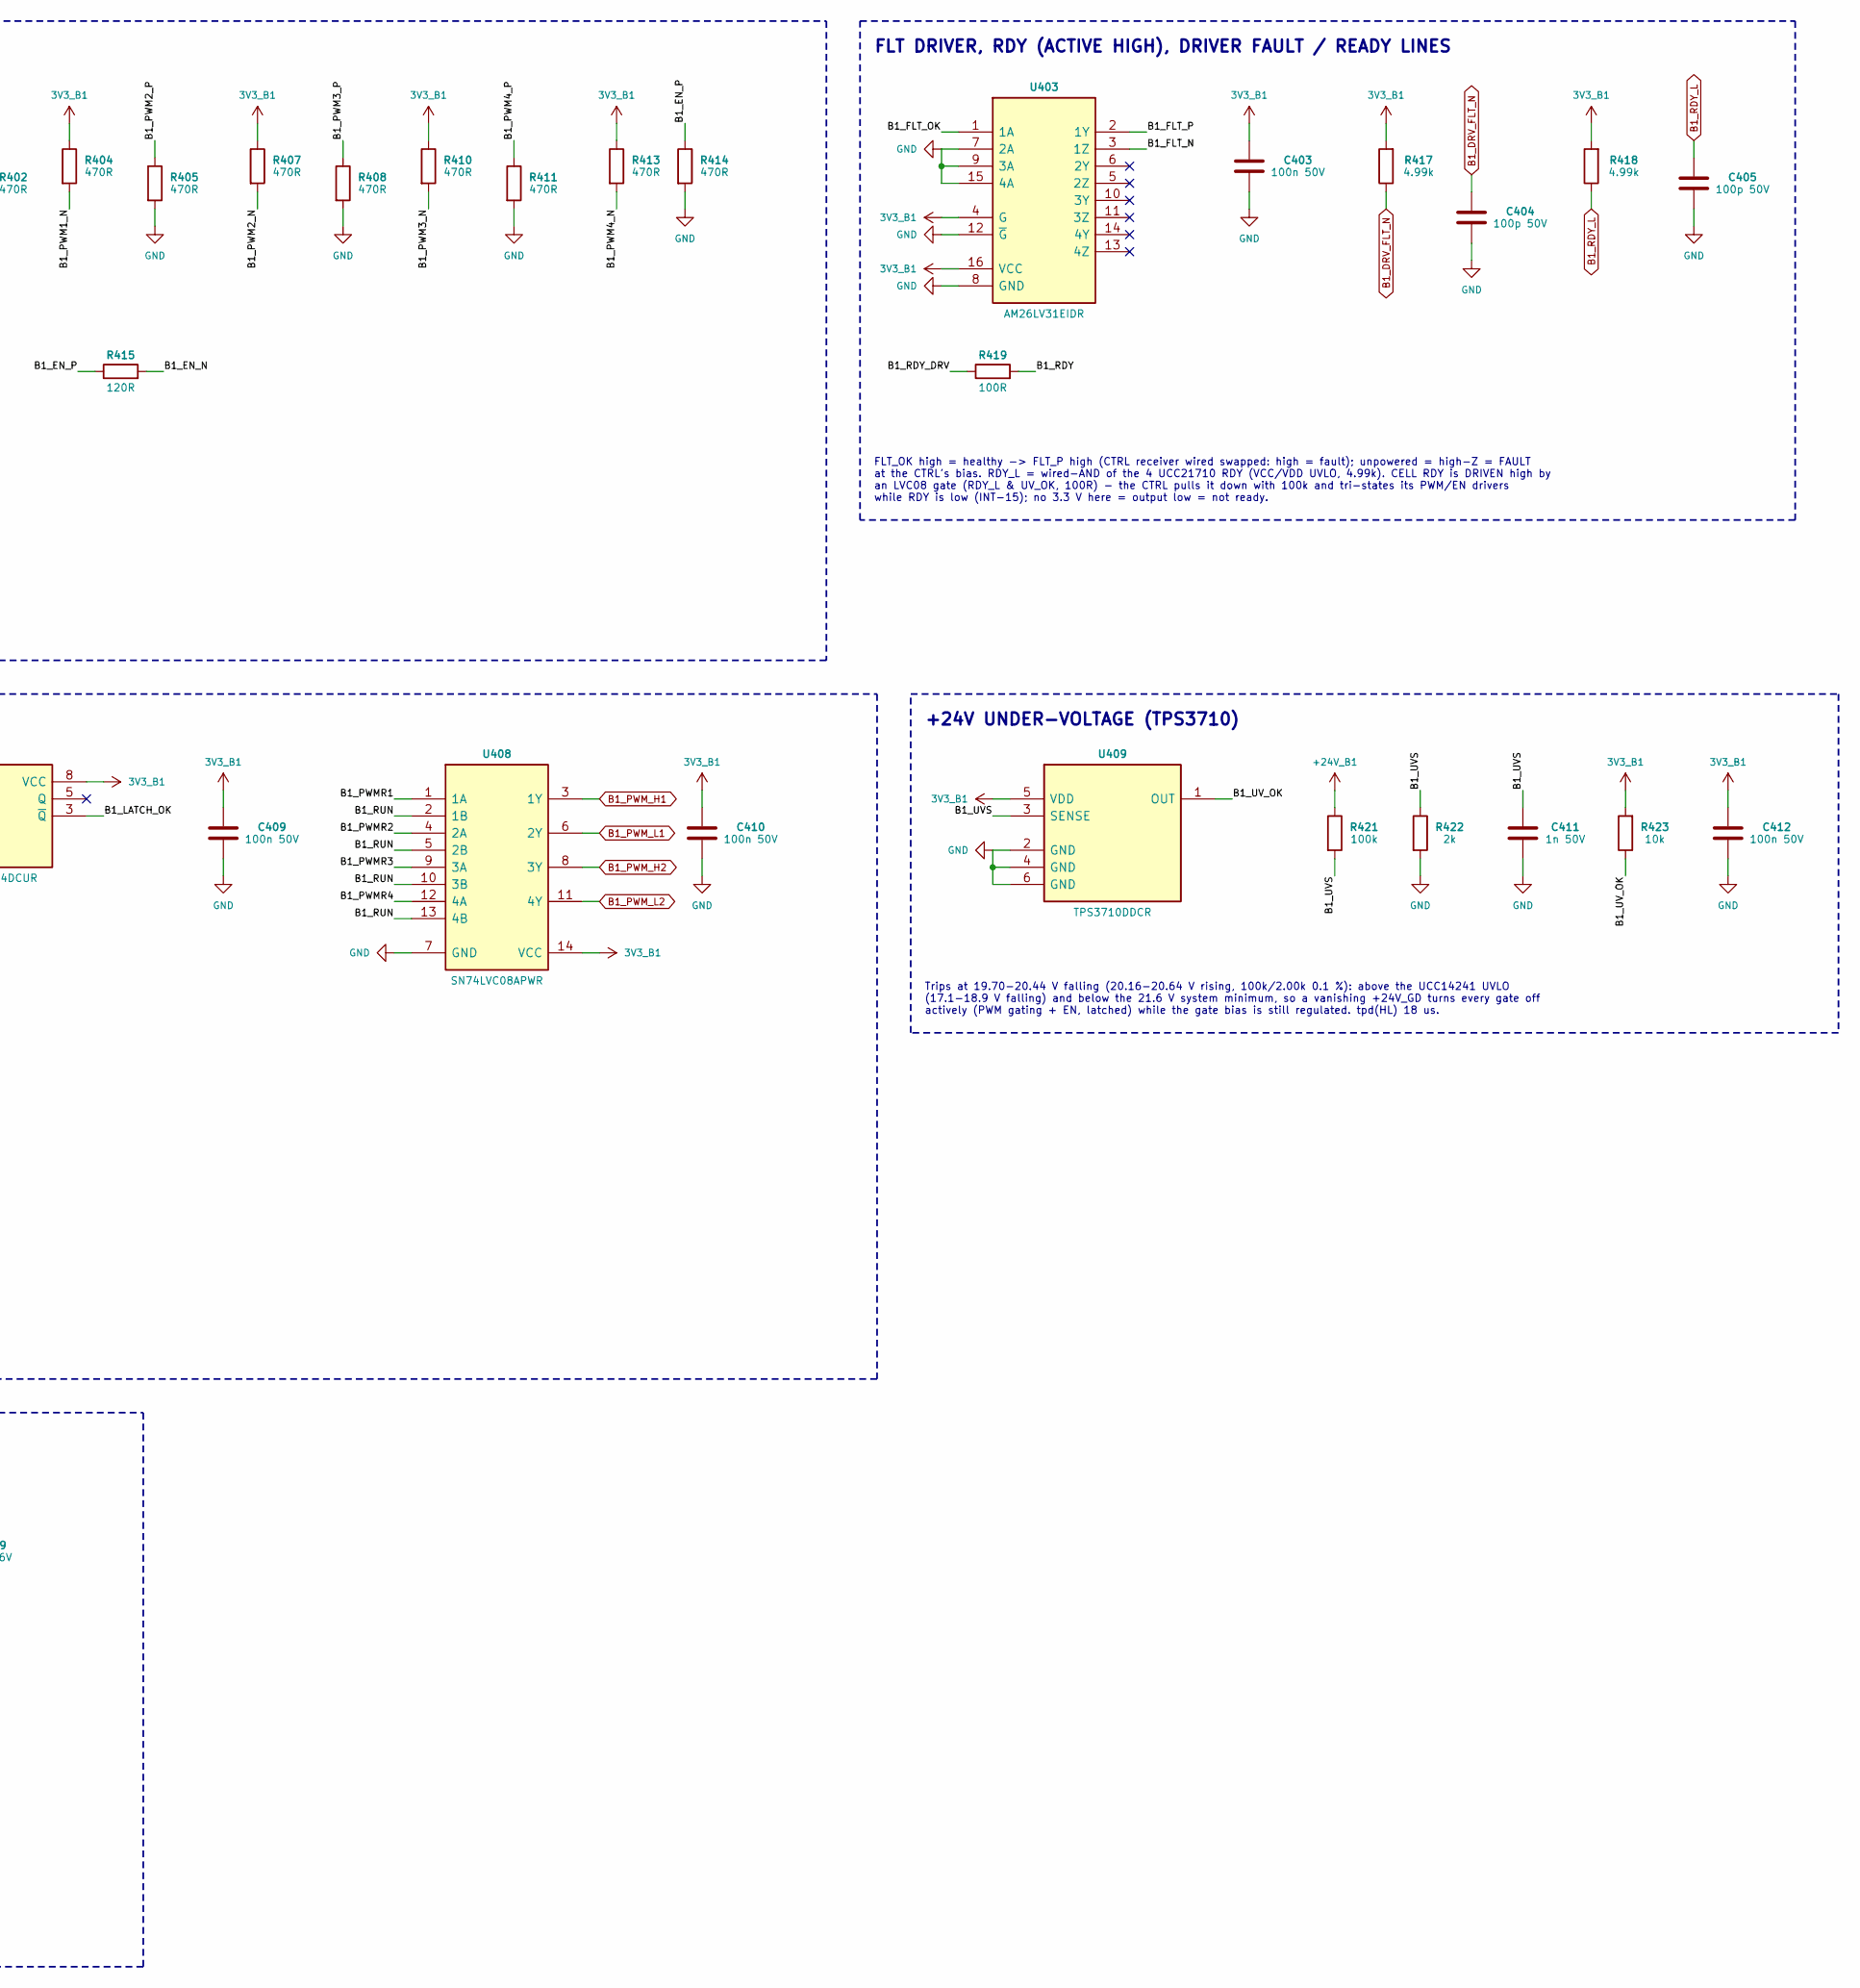
[picture p223: schematic 04_b1_if.kicad_sch, part in row 1, column 2]

Parts:
C401, C402, C403, C406, C407, C408, C409, C410, C412, C415: 100n 50V
C404, C405: 100p 50V
C411: 1n 50V
C413: 4.7u 50V
C414: 220n 50V
C416, C419: 1u 16V
C417, C418: 22u 10V
C420: 2.2u 16V
J401: 61204021621; MPN 61204021621
L401: 74439346100; MPN 74439346100
R401: 20.0k
R402, R404, R405, R407, R408, R410, R411, R413, R414, R416: 470R
R403, R406, R409, R412, R415: 120R
R417, R418: 4.99k
R419: 100R
R420, R423: 10k
R421, R424: 100k
R422: 2k
R425: 24.9k
TP401, TP402, TP403: TP
U401, U402: AM26LV32EIDR; MPN AM26LV32EIDR
U403: AM26LV31EIDR; MPN AM26LV31EIDR
U404, U405, U406, U408: SN74LVC08APWR; MPN SN74LVC08APWR
U407: SN74LVC1G74DCUR; MPN SN74LVC1G74DCUR
U409: TPS3710DDCR; MPN TPS3710DDCR
U410: LMR36015ARNXR; MPN LMR36015ARNXR
U411: TPS7A2033PDBVR; MPN TPS7A2033PDBVR

Connections:
3V3_B1: C401.1, C402.1, C403.1, C406.1, C407.1, C408.1, C409.1, C410.1, C412.1, C420.1, R404.1, R407.1, R410.1, R413.1, R416.1, R417.2, R418.2, R423.2, TP403.1, U401.4 (G), U401.16 (VCC), U402.4 (G), U402.16 (VCC), U403.4 (G), U403.16 (VCC), U404.14 (VCC), U405.14 (VCC), U406.14 (VCC), U407.8 (VCC), U408.14 (VCC), U409.5 (VDD), U411.5 (OUT)
5V_B1: C417.1, C418.1, C419.1, L401.2, R424.1, U411.1 (IN), U411.3 (EN)
+24V_B1: C413.1, C414.1, J401.1, J401.2, R421.1, U410.2 (VIN), U410.9 (EN), U410.10 (VIN)
AGND: J401.34, J401.36, J401.37, J401.38
B1_AN1_N: J401.32
B1_AN1_P: J401.31
B1_AN2_P: J401.33
B1_AN3_P: J401.35
B1_BOOT: C415.1, U410.4 (BOOT)
B1_DCH_OK: U404.4 (2A)
B1_DCL_OK: U404.5 (2B)
B1_DC_OK: U404.6 (2Y), U404.10 (3B)
B1_DRV_FLT_N: C404.1, R417.1, U405.13 (4B), U406.2 (1B)
B1_EN_DRV: R420.1, TP401.1, U405.8 (3Y), U405.12 (4A)
B1_EN_N: J401.28, R415.2, R416.2, U402.1 (1B)
B1_EN_P: J401.27, R414.1, R415.1, U402.2 (1A)
B1_EN_RX: U402.3 (1Y), U405.9 (3A), U407.6 (~CLR)
B1_FB5: R424.2, R425.1, U410.7 (FB)
B1_FLT_N: J401.26, U403.3 (1Z)
B1_FLT_OK: U403.1 (1A), U406.6 (2Y)
B1_FLT_P: J401.25, U403.2 (1Y)
B1_H_OK: U406.3 (1Y), U406.4 (2A)
B1_ID: J401.30, R401.1
B1_IV_OK: U404.11 (4Y), U405.1 (1A)
B1_I_OK: U404.8 (3Y), U404.12 (4A)
B1_LATCH_OK: U405.4 (2A), U407.3 (~Q)
B1_LR_OK: U405.6 (2Y), U405.10 (3B), U406.1 (1A)
B1_OCH_OK: U404.1 (1A)
B1_OCL_OK: U404.2 (1B)
B1_OC_OK: U404.3 (1Y), U404.9 (3A)
B1_PWM1_N: J401.6, R403.2, R404.2, U401.1 (1B)
B1_PWM1_P: J401.5, R402.1, R403.1, U401.2 (1A)
B1_PWM2_N: J401.8, R406.2, R407.2, U401.7 (2B)
B1_PWM2_P: J401.7, R405.1, R406.1, U401.6 (2A)
B1_PWM3_N: J401.10, R409.2, R410.2, U401.9 (3B)
B1_PWM3_P: J401.9, R408.1, R409.1, U401.10 (3A)
B1_PWM4_N: J401.12, R412.2, R413.2, U401.15 (4B)
B1_PWM4_P: J401.11, R411.1, R412.1, U401.14 (4A)
B1_PWMR1: U401.3 (1Y), U408.1 (1A)
B1_PWMR2: U401.5 (2Y), U408.4 (2A)
B1_PWMR3: U401.11 (3Y), U408.9 (3A)
B1_PWMR4: U401.13 (4Y), U408.12 (4A)
B1_PWM_H1: U408.3 (1Y)
B1_PWM_H2: U408.8 (3Y)
B1_PWM_L1: U408.6 (2Y)
B1_PWM_L2: U408.11 (4Y)
B1_RDY: J401.29, R419.2
B1_RDY_DRV: R419.1, U406.8 (3Y)
B1_RDY_L: C405.1, R418.1, U405.5 (2B), U406.9 (3A)
B1_RUN: U405.11 (4Y), U408.2 (1B), U408.5 (2B), U408.10 (3B), U408.13 (4B)
B1_SW: C415.2, L401.1, U410.12 (SW)
B1_TRIP_N: TP402.1, U405.3 (1Y), U406.5 (2B), U407.7 (~PRE)
B1_UVS: C411.1, R421.2, R422.1, U409.3 (SENSE)
B1_UV_OK: R423.1, U405.2 (1B), U406.10 (3B), U409.1 (OUT)
B1_VCC5: C416.1, U410.5 (VCC)
GND: C401.2, C402.2, C403.2, C404.2, C405.2, C406.2, C407.2, C408.2, C409.2, C410.2, C411.2, C412.2, C413.2, C414.2, C416.2, C417.2, C418.2, C419.2, C420.2, J401.3, J401.4, J401.13, J401.14, J401.23, J401.24, R401.2, R402.2, R405.2, R408.2, R411.2, R414.2, R420.2, R422.2, R425.2, U401.8 (GND), U401.12 (~G), U402.8 (GND), U402.12 (~G), U403.7 (2A), U403.8 (GND), U403.9 (3A), U403.12 (~G), U403.15 (4A), U404.7 (GND), U405.7 (GND), U406.7 (GND), U406.12 (4A), U406.13 (4B), U407.1 (CLK), U407.2 (D), U407.4 (GND), U408.7 (GND), U409.2 (GND), U409.4 (GND), U409.6 (GND), U410.1 (PGND), U410.6 (AGND), U410.11 (PGND), U411.2 (GND)
OV_OK: U404.13 (4B)

Notes on the sheet:
SNVSB49D table 10-3 (5 V, 400 kHz): 10 uH, 2 x 22 uF, 100k / 24.9k -> 5.02 V. EN tied to VIN. 5 V: UCC12050 (HV-side sensor), AMC3330, PELV op amps / comparator / reference; 3.3 V: receivers, logic, ISO7720F side 2, UCC21710 VCC, bias ENA.
RS-422 RECEIVERS WITH FAIL-SAFE BIAS (PWM1-4, EN)
Each pair: P 470R to GND, N 470R to 3.3 V, 120R across (= termination). AM26LV32E: VID <= -0.2 V -> output LOW. Cable unplugged / pair open: VID <= -0.303 V worst case (3.135 V, 1 %, ri 4 k) -> LOW = gate off. CTRL unpowered: its AM26LV31E outputs are high-Z (IO(OFF) <= 100 uA) -> VID <= -0.293 V -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
+24V UNDER-VOLTAGE (TPS3710)
interfaces.CELL. PWM1/2 = leg A high/low, PWM3/4 = leg B high/low. PWM5-8 and NTC_P/N not used (open). AN2_N / AN3_N = AGND (single-ended 0-3 V). +24V = +24V_GD from the CTRL eFuse (safety channel B): this board draws <= 1.0 A and presents <= 600 uF to it (design_check).
FLT DRIVER, RDY (ACTIVE HIGH), DRIVER FAULT / READY LINES
TRIP LATCH, ENABLES, FLT (NO FIRMWARE IN THE PATH; INT-17, INT-18)
TRIP_N = OC_H & OC_L & DC_H & DC_L & OV_OK & UV_OK -> LVC1G74 PRE: LATCH_OK low until the CTRL takes EN low (CLR). LR_OK = LATCH_OK & RDY_L. EN_DRV = EN_RX & LR_OK -> RST/EN of the 4 drivers (<= 0.8 us filter, clears DESAT latches). RUN = EN_DRV & DRV_FLT_N gates every PWM (fast path ~0.25 us): a t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
Trips at 19.70-20.44 V falling (20.16-20.64 V rising, 100k/2.00k 0.1 %): above the UCC14241 UVLO (17.1-18.9 V falling) and below the 21.6 V system minimum, so a vanishing +24V_GD turns every gate off actively (PWM gating + EN, latched) while the gate bias is still regulated. tpd(HL) 18 us.
LOCAL 5 V (LMR36015) AND 3.3 V (TPS7A2033) FROM THE CELL +24V
FLT_OK high = healthy -> FLT_P high (CTRL receiver wired swapped: high = fault); unpowered = high-Z = FAULT at the CTRL's bias. RDY_L = wired-AND of the 4 UCC21710 RDY (VCC/VDD UVLO, 4.99k). CELL RDY is DRIVEN high by an LVC08 gate (RDY_L & UV_OK, 100R) - the CTRL pulls it down with 100k and tri-st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
CELL CONNECTOR -> CTRL-C2000 PORT C1 (HRPWM EPWM1-2)
