vectivolt/PCM/hardware/DAB60/sheets/05_b1_sense.kicad_sch

## KiCad design hardware/DAB60/sheets/05_b1_sense.kicad_sch (2026-10-04)

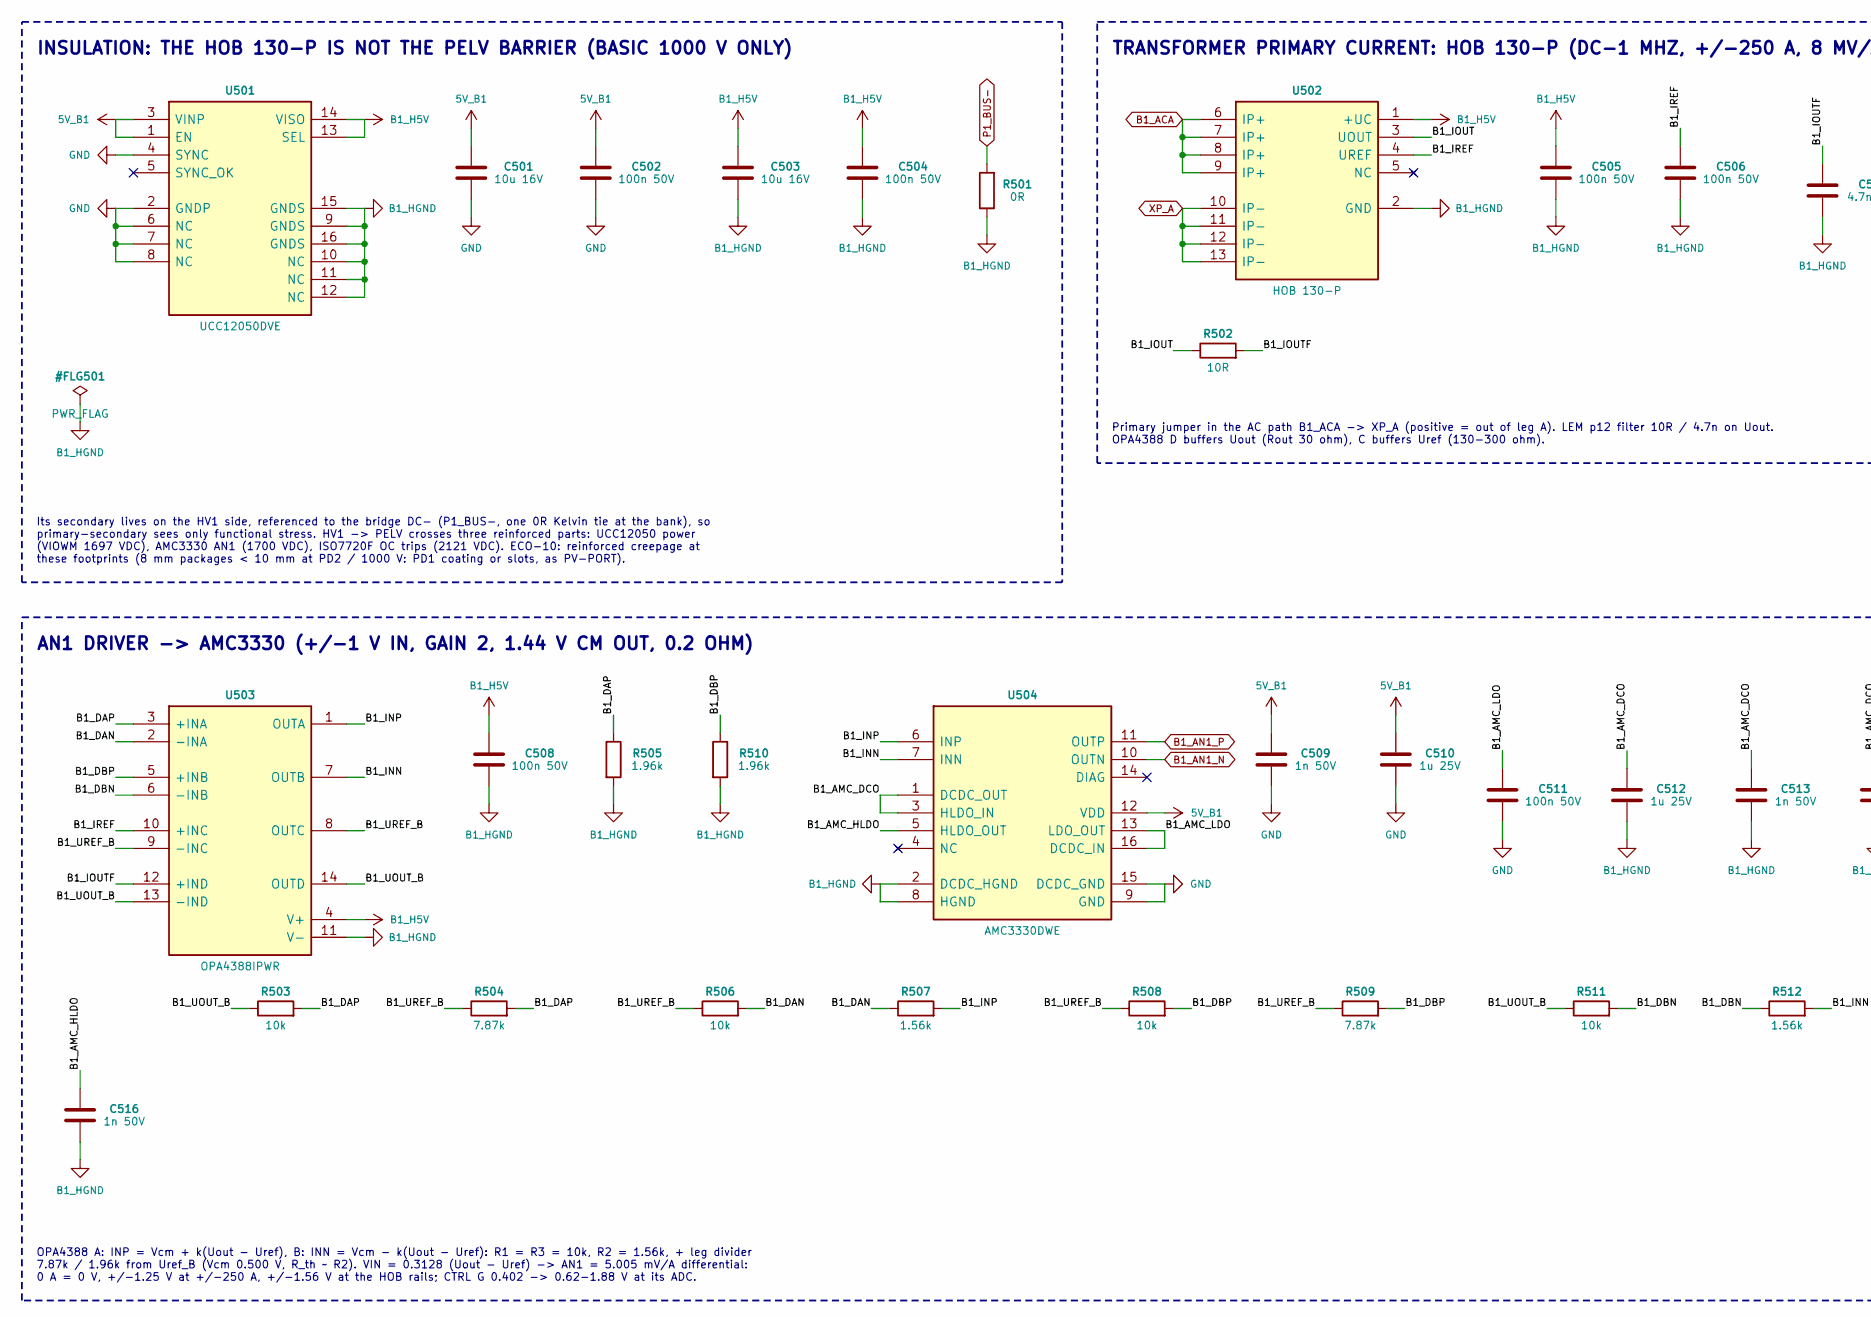
[picture p224: schematic 05_b1_sense.kicad_sch, part in row 1, column 1]

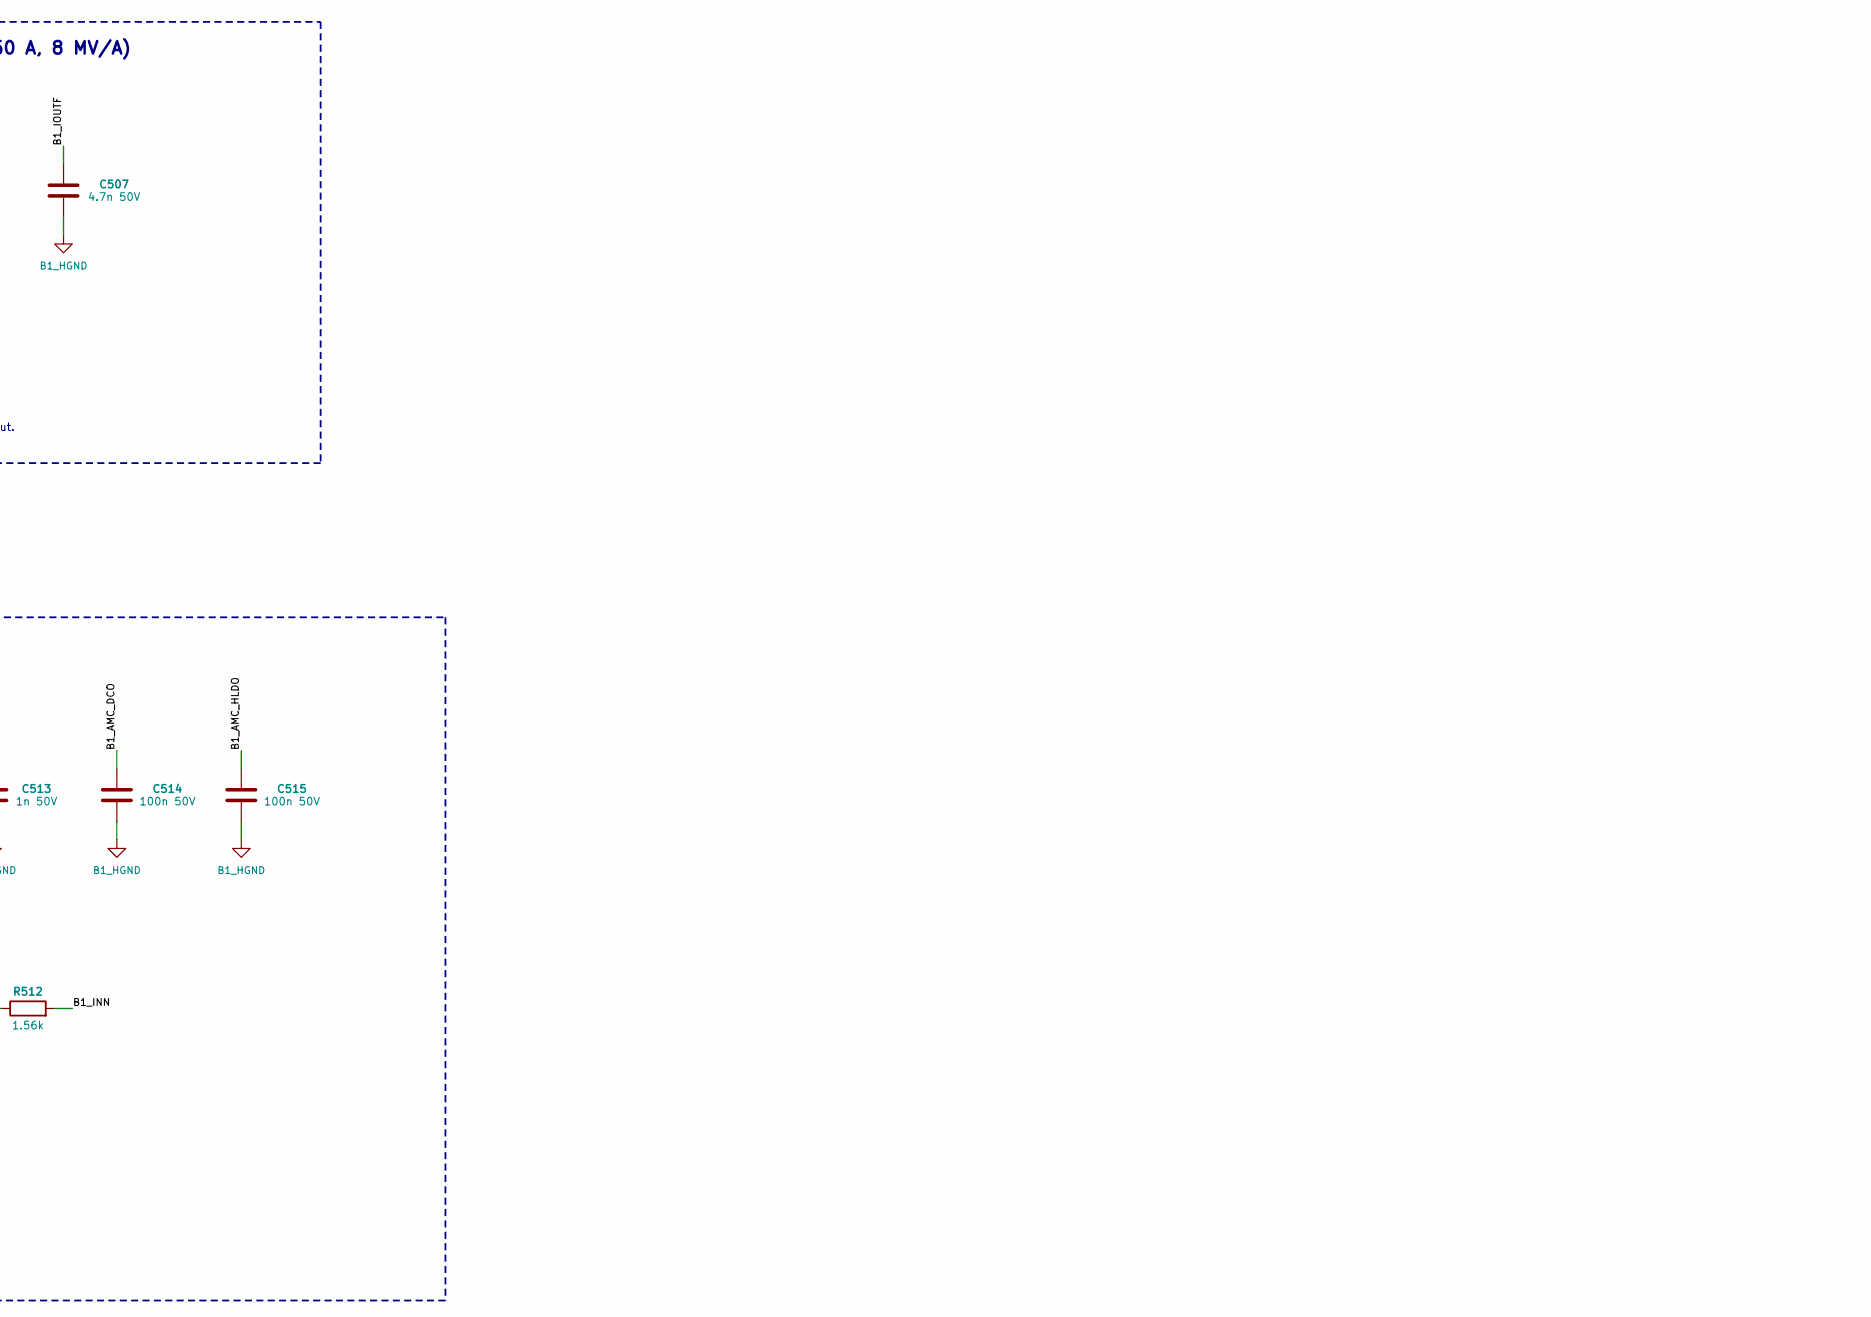
[picture p225: schematic 05_b1_sense.kicad_sch, part in row 1, column 2]

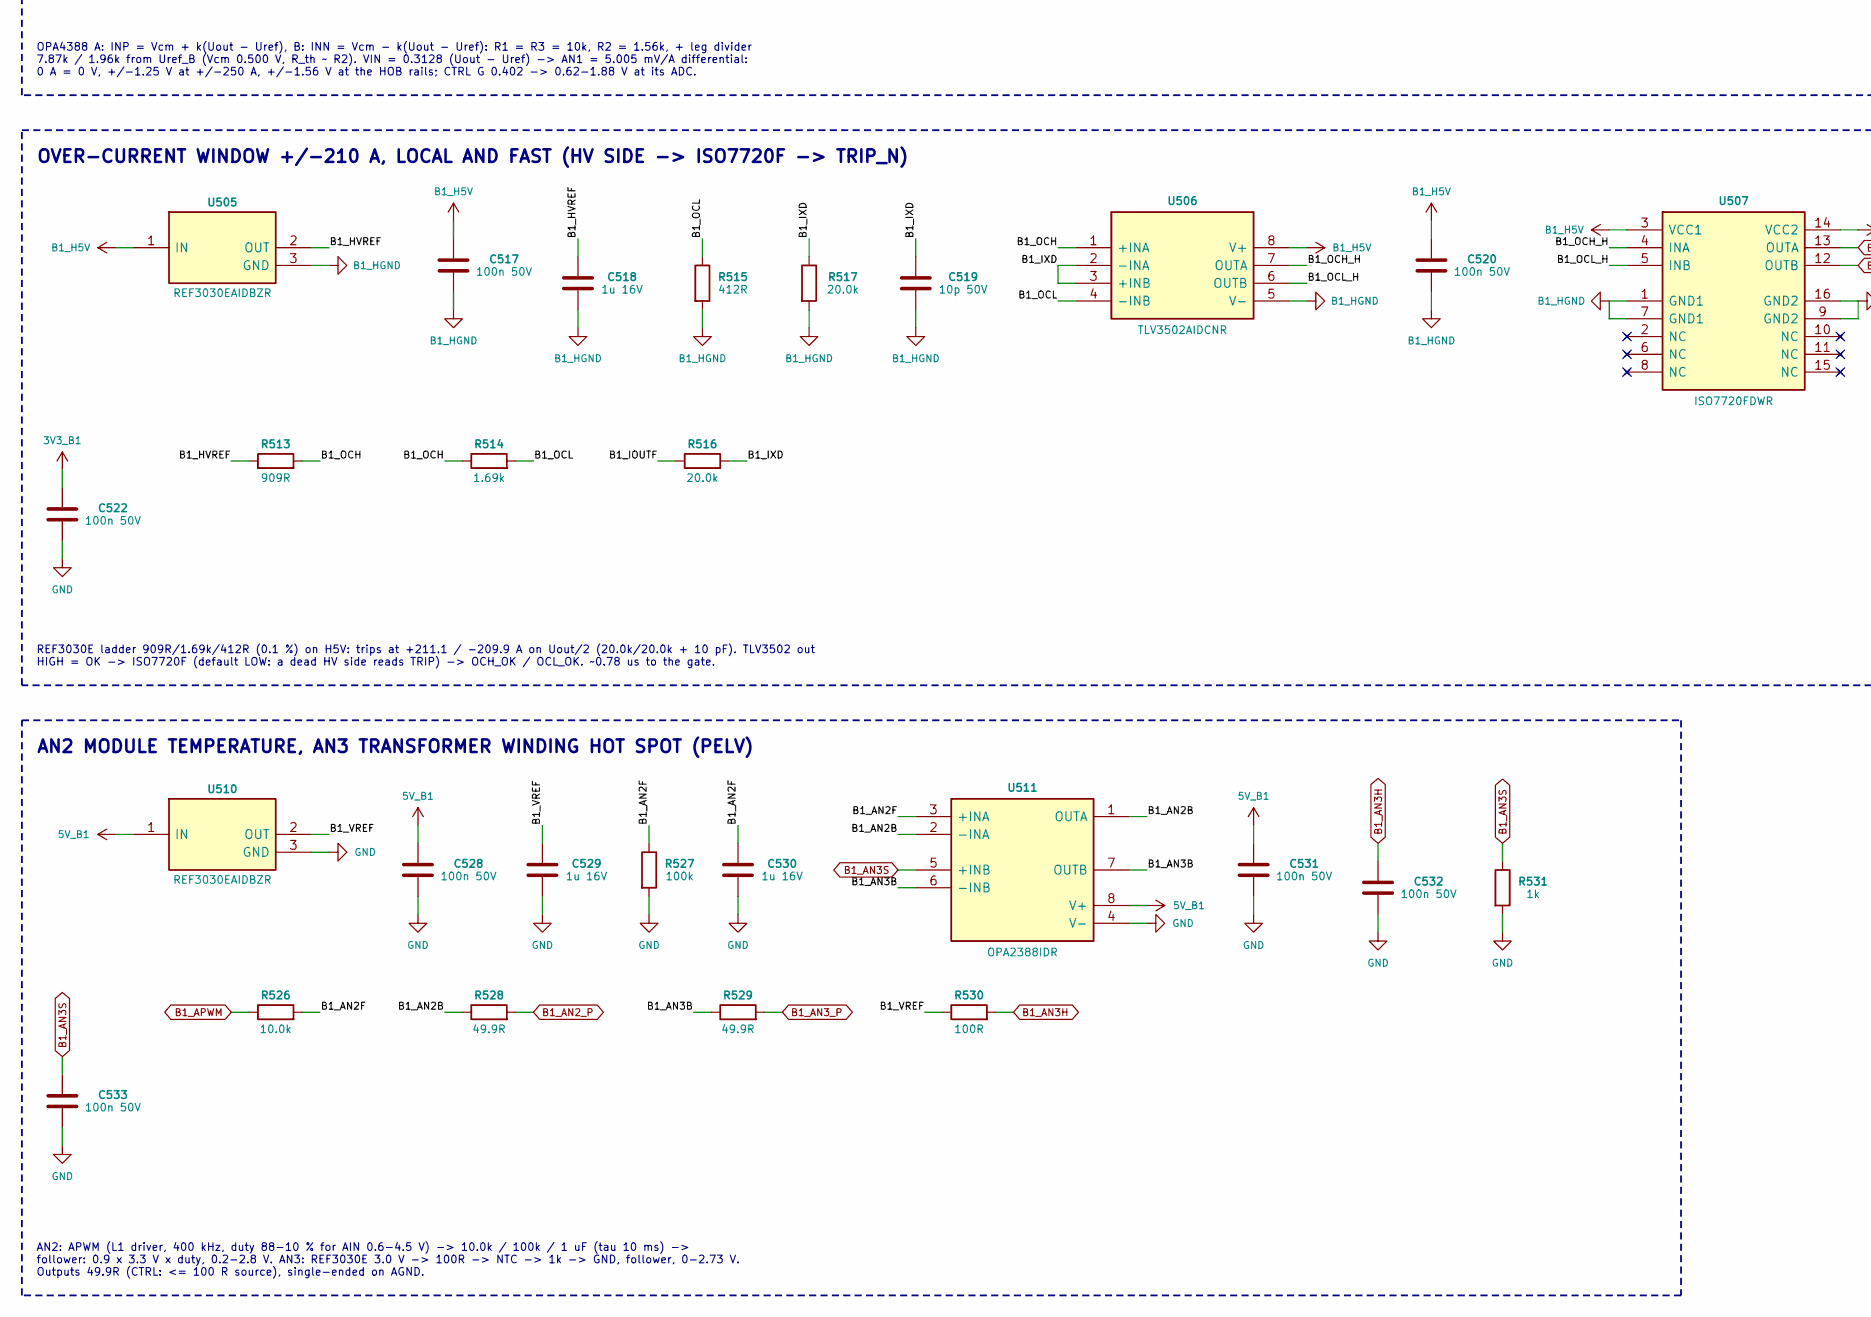
[picture p226: schematic 05_b1_sense.kicad_sch, part in row 2, column 1]

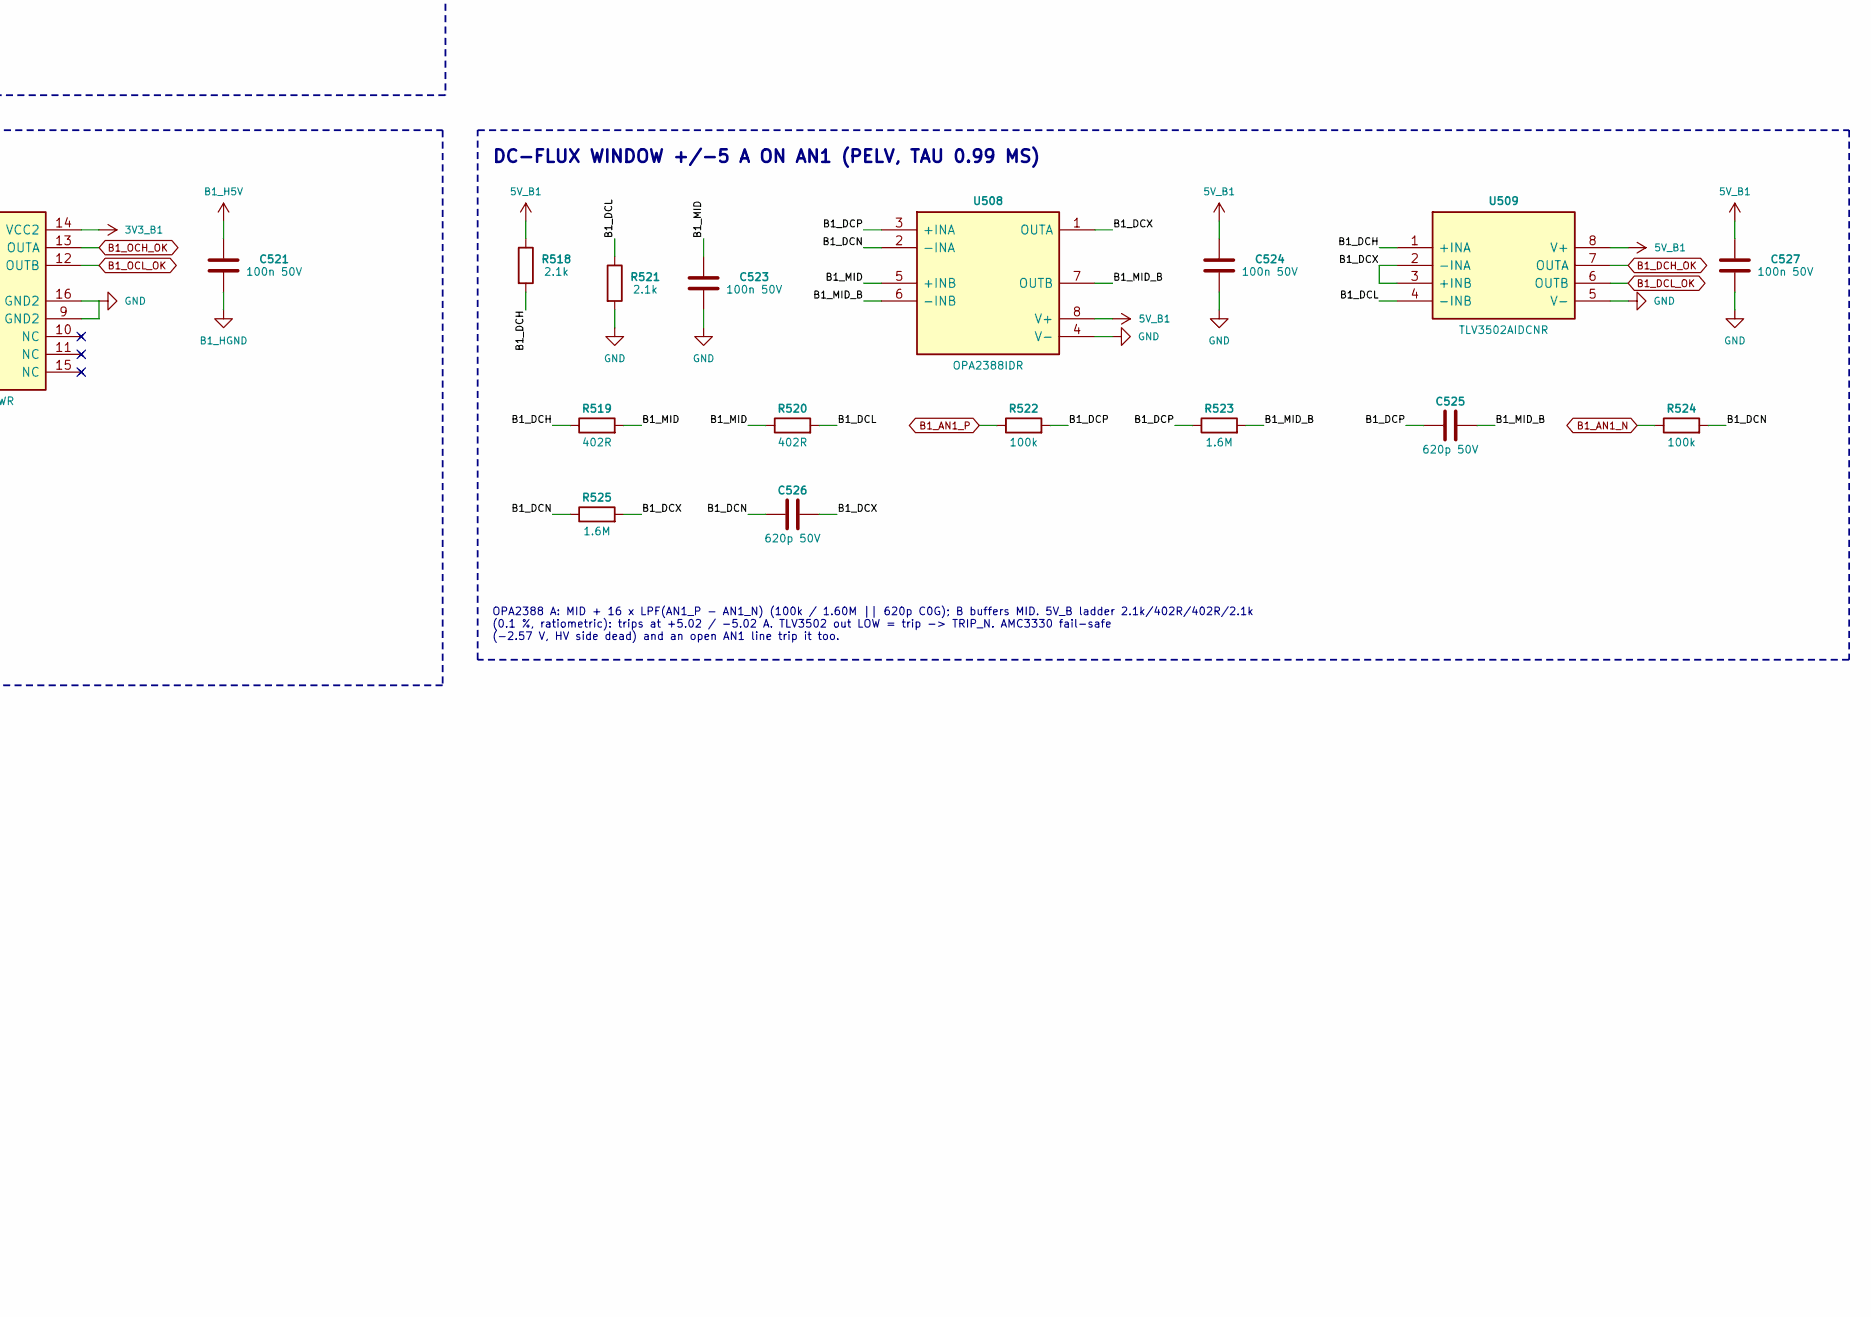
[picture p227: schematic 05_b1_sense.kicad_sch, part in row 2, column 2]

Parts:
C501, C503: 10u 16V
C502, C504, C505, C506, C508, C511, C514, C515, C517, C520, C521, C522, C523, C524, C527, C528, C531, C532, C533: 100n 50V
C507: 4.7n 50V
C509, C513, C516: 1n 50V
C510, C512: 1u 25V
C518, C529, C530: 1u 16V
C519: 10p 50V
C525, C526: 620p 50V
R501: 0R
R502: 10R
R503, R506, R508, R511: 10k
R504, R509: 7.87k
R505, R510: 1.96k
R507, R512: 1.56k
R513: 909R
R514: 1.69k
R515: 412R
R516, R517: 20.0k
R518, R521: 2.1k
R519, R520: 402R
R522, R524, R527: 100k
R523, R525: 1.6M
R526: 10.0k
R528, R529: 49.9R
R530: 100R
R531: 1k
U501: UCC12050DVE; MPN UCC12050DVE
U502: HOB 130-P; MPN HOB 130-P
U503: OPA4388IPWR; MPN OPA4388IPWR
U504: AMC3330DWE; MPN AMC3330DWE
U505, U510: REF3030EAIDBZR; MPN REF3030EAIDBZR
U506, U509: TLV3502AIDCNR; MPN TLV3502AIDCNR
U507: ISO7720FDWR; MPN ISO7720FDWR
U508, U511: OPA2388IDR; MPN OPA2388IDR

Connections:
3V3_B1: C522.1, U507.14 (VCC2)
5V_B1: C501.1, C502.1, C509.1, C510.1, C524.1, C527.1, C528.1, C531.1, R518.1, U501.1 (EN), U501.3 (VINP), U504.12 (VDD), U508.8 (V+), U509.8 (V+), U510.1 (IN), U511.8 (V+)
B1_ACA: U502.6 (IP+), U502.7 (IP+), U502.8 (IP+), U502.9 (IP+)
B1_AMC_DCO: C512.1, C513.1, C514.1, U504.1 (DCDC_OUT), U504.3 (HLDO_IN)
B1_AMC_HLDO: C515.1, C516.1, U504.5 (HLDO_OUT)
B1_AMC_LDO: C511.1, U504.13 (LDO_OUT), U504.16 (DCDC_IN)
B1_AN1_N: R524.1, U504.10 (OUTN)
B1_AN1_P: R522.1, U504.11 (OUTP)
B1_AN2B: R528.1, U511.1 (OUTA), U511.2 (-INA)
B1_AN2F: C530.1, R526.2, R527.1, U511.3 (+INA)
B1_AN2_P: R528.2
B1_AN3B: R529.1, U511.6 (-INB), U511.7 (OUTB)
B1_AN3H: C532.1, R530.2
B1_AN3S: C533.1, R531.1, U511.5 (+INB)
B1_AN3_P: R529.2
B1_APWM: R526.1
B1_DAN: R506.2, R507.1, U503.2 (-INA)
B1_DAP: R503.2, R504.2, R505.1, U503.3 (+INA)
B1_DBN: R511.2, R512.1, U503.6 (-INB)
B1_DBP: R508.2, R509.2, R510.1, U503.5 (+INB)
B1_DCH: R518.2, R519.1, U509.1 (+INA)
B1_DCH_OK: U509.7 (OUTA)
B1_DCL: R520.2, R521.1, U509.4 (-INB)
B1_DCL_OK: U509.6 (OUTB)
B1_DCN: C526.1, R524.2, R525.1, U508.2 (-INA)
B1_DCP: C525.1, R522.2, R523.1, U508.3 (+INA)
B1_DCX: C526.2, R525.2, U508.1 (OUTA), U509.2 (-INA), U509.3 (+INB)
B1_H5V: C503.1, C504.1, C505.1, C508.1, C517.1, C520.1, C521.1, U501.13 (SEL), U501.14 (VISO), U502.1 (+UC), U503.4 (V+), U505.1 (IN), U506.8 (V+), U507.3 (VCC1)
B1_HGND: C503.2, C504.2, C505.2, C506.2, C507.2, C508.2, C512.2, C513.2, C514.2, C515.2, C516.2, C517.2, C518.2, C519.2, C520.2, C521.2, R501.1, R505.2, R510.2, R515.2, R517.2, U501.9 (GNDS), U501.10 (NC), U501.11 (NC), U501.12 (NC), U501.15 (GNDS), U501.16 (GNDS), U502.2 (GND), U503.11 (V-), U504.2 (DCDC_HGND), U504.8 (HGND), U505.3 (GND), U506.5 (V-), U507.1 (GND1), U507.7 (GND1)
B1_HVREF: C518.1, R513.1, U505.2 (OUT)
B1_INN: R512.2, U503.7 (OUTB), U504.7 (INN)
B1_INP: R507.2, U503.1 (OUTA), U504.6 (INP)
B1_IOUT: R502.1, U502.3 (UOUT)
B1_IOUTF: C507.1, R502.2, R516.1, U503.12 (+IND)
B1_IREF: C506.1, U502.4 (UREF), U503.10 (+INC)
B1_IXD: C519.1, R516.2, R517.1, U506.2 (-INA), U506.3 (+INB)
B1_MID: C523.1, R519.2, R520.1, U508.5 (+INB)
B1_MID_B: C525.2, R523.2, U508.6 (-INB), U508.7 (OUTB)
B1_OCH: R513.2, R514.1, U506.1 (+INA)
B1_OCH_H: U506.7 (OUTA), U507.4 (INA)
B1_OCH_OK: U507.13 (OUTA)
B1_OCL: R514.2, R515.1, U506.4 (-INB)
B1_OCL_H: U506.6 (OUTB), U507.5 (INB)
B1_OCL_OK: U507.12 (OUTB)
B1_UOUT_B: R503.1, R511.1, U503.13 (-IND), U503.14 (OUTD)
B1_UREF_B: R504.1, R506.1, R508.1, R509.1, U503.8 (OUTC), U503.9 (-INC)
B1_VREF: C529.1, R530.1, U510.2 (OUT)
GND: C501.2, C502.2, C509.2, C510.2, C511.2, C522.2, C523.2, C524.2, C527.2, C528.2, C529.2, C530.2, C531.2, C532.2, C533.2, R521.2, R527.2, R531.2, U501.2 (GNDP), U501.4 (SYNC), U501.6 (NC), U501.7 (NC), U501.8 (NC), U504.9 (GND), U504.15 (DCDC_GND), U507.9 (GND2), U507.16 (GND2), U508.4 (V-), U509.5 (V-), U510.3 (GND), U511.4 (V-)
P1_BUS-: R501.2
XP_A: U502.10 (IP-), U502.11 (IP-), U502.12 (IP-), U502.13 (IP-)

Notes on the sheet:
Its secondary lives on the HV1 side, referenced to the bridge DC- (P1_BUS-, one 0R Kelvin tie at the bank), so primary-secondary sees only functional stress. HV1 -> PELV crosses three reinforced parts: UCC12050 power (VIOWM 1697 VDC), AMC3330 AN1 (1700 VDC), ISO7720F OC trips (2121 VDC). ECO-10: re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
AN1 DRIVER -> AMC3330 (+/-1 V IN, GAIN 2, 1.44 V CM OUT, 0.2 OHM)
OPA2388 A: MID + 16 x LPF(AN1_P - AN1_N) (100k / 1.60M || 620p C0G); B buffers MID. 5V_B ladder 2.1k/402R/402R/2.1k (0.1 %, ratiometric): trips at +5.02 / -5.02 A. TLV3502 out LOW = trip -> TRIP_N. AMC3330 fail-safe (-2.57 V, HV side dead) and an open AN1 line trip it too.
Primary jumper in the AC path B1_ACA -> XP_A (positive = out of leg A). LEM p12 filter 10R / 4.7n on Uout. OPA4388 D buffers Uout (Rout 30 ohm), C buffers Uref (130-300 ohm).
DC-FLUX WINDOW +/-5 A ON AN1 (PELV, TAU 0.99 MS)
AN2: APWM (L1 driver, 400 kHz, duty 88-10 % for AIN 0.6-4.5 V) -> 10.0k / 100k / 1 uF (tau 10 ms) -> follower: 0.9 x 3.3 V x duty, 0.2-2.8 V. AN3: REF3030E 3.0 V -> 100R -> NTC -> 1k -> GND, follower, 0-2.73 V. Outputs 49.9R (CTRL: <= 100 R source), single-ended on AGND.
AN2 MODULE TEMPERATURE, AN3 TRANSFORMER WINDING HOT SPOT (PELV)
INSULATION: THE HOB 130-P IS NOT THE PELV BARRIER (BASIC 1000 V ONLY)
OPA4388 A: INP = Vcm + k(Uout - Uref), B: INN = Vcm - k(Uout - Uref): R1 = R3 = 10k, R2 = 1.56k, + leg divider 7.87k / 1.96k from Uref_B (Vcm 0.500 V, R_th ~ R2). VIN = 0.3128 (Uout - Uref) -> AN1 = 5.005 mV/A differential: 0 A = 0 V, +/-1.25 V at +/-250 A, +/-1.56 V at the HOB rails; CTRL G 0.402 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
REF3030E ladder 909R/1.69k/412R (0.1 %) on H5V: trips at +211.1 / -209.9 A on Uout/2 (20.0k/20.0k + 10 pF). TLV3502 out HIGH = OK -> ISO7720F (default LOW: a dead HV side reads TRIP) -> OCH_OK / OCL_OK. ~0.78 us to the gate.
TRANSFORMER PRIMARY CURRENT: HOB 130-P (DC-1 MHZ, +/-250 A, 8 MV/A)
OVER-CURRENT WINDOW +/-210 A, LOCAL AND FAST (HV SIDE -> ISO7720F -> TRIP_N)
