vectivolt/PCM/hardware/DAB60/sheets/06_b2_power.kicad_sch

## KiCad design hardware/DAB60/sheets/06_b2_power.kicad_sch (2026-10-04)

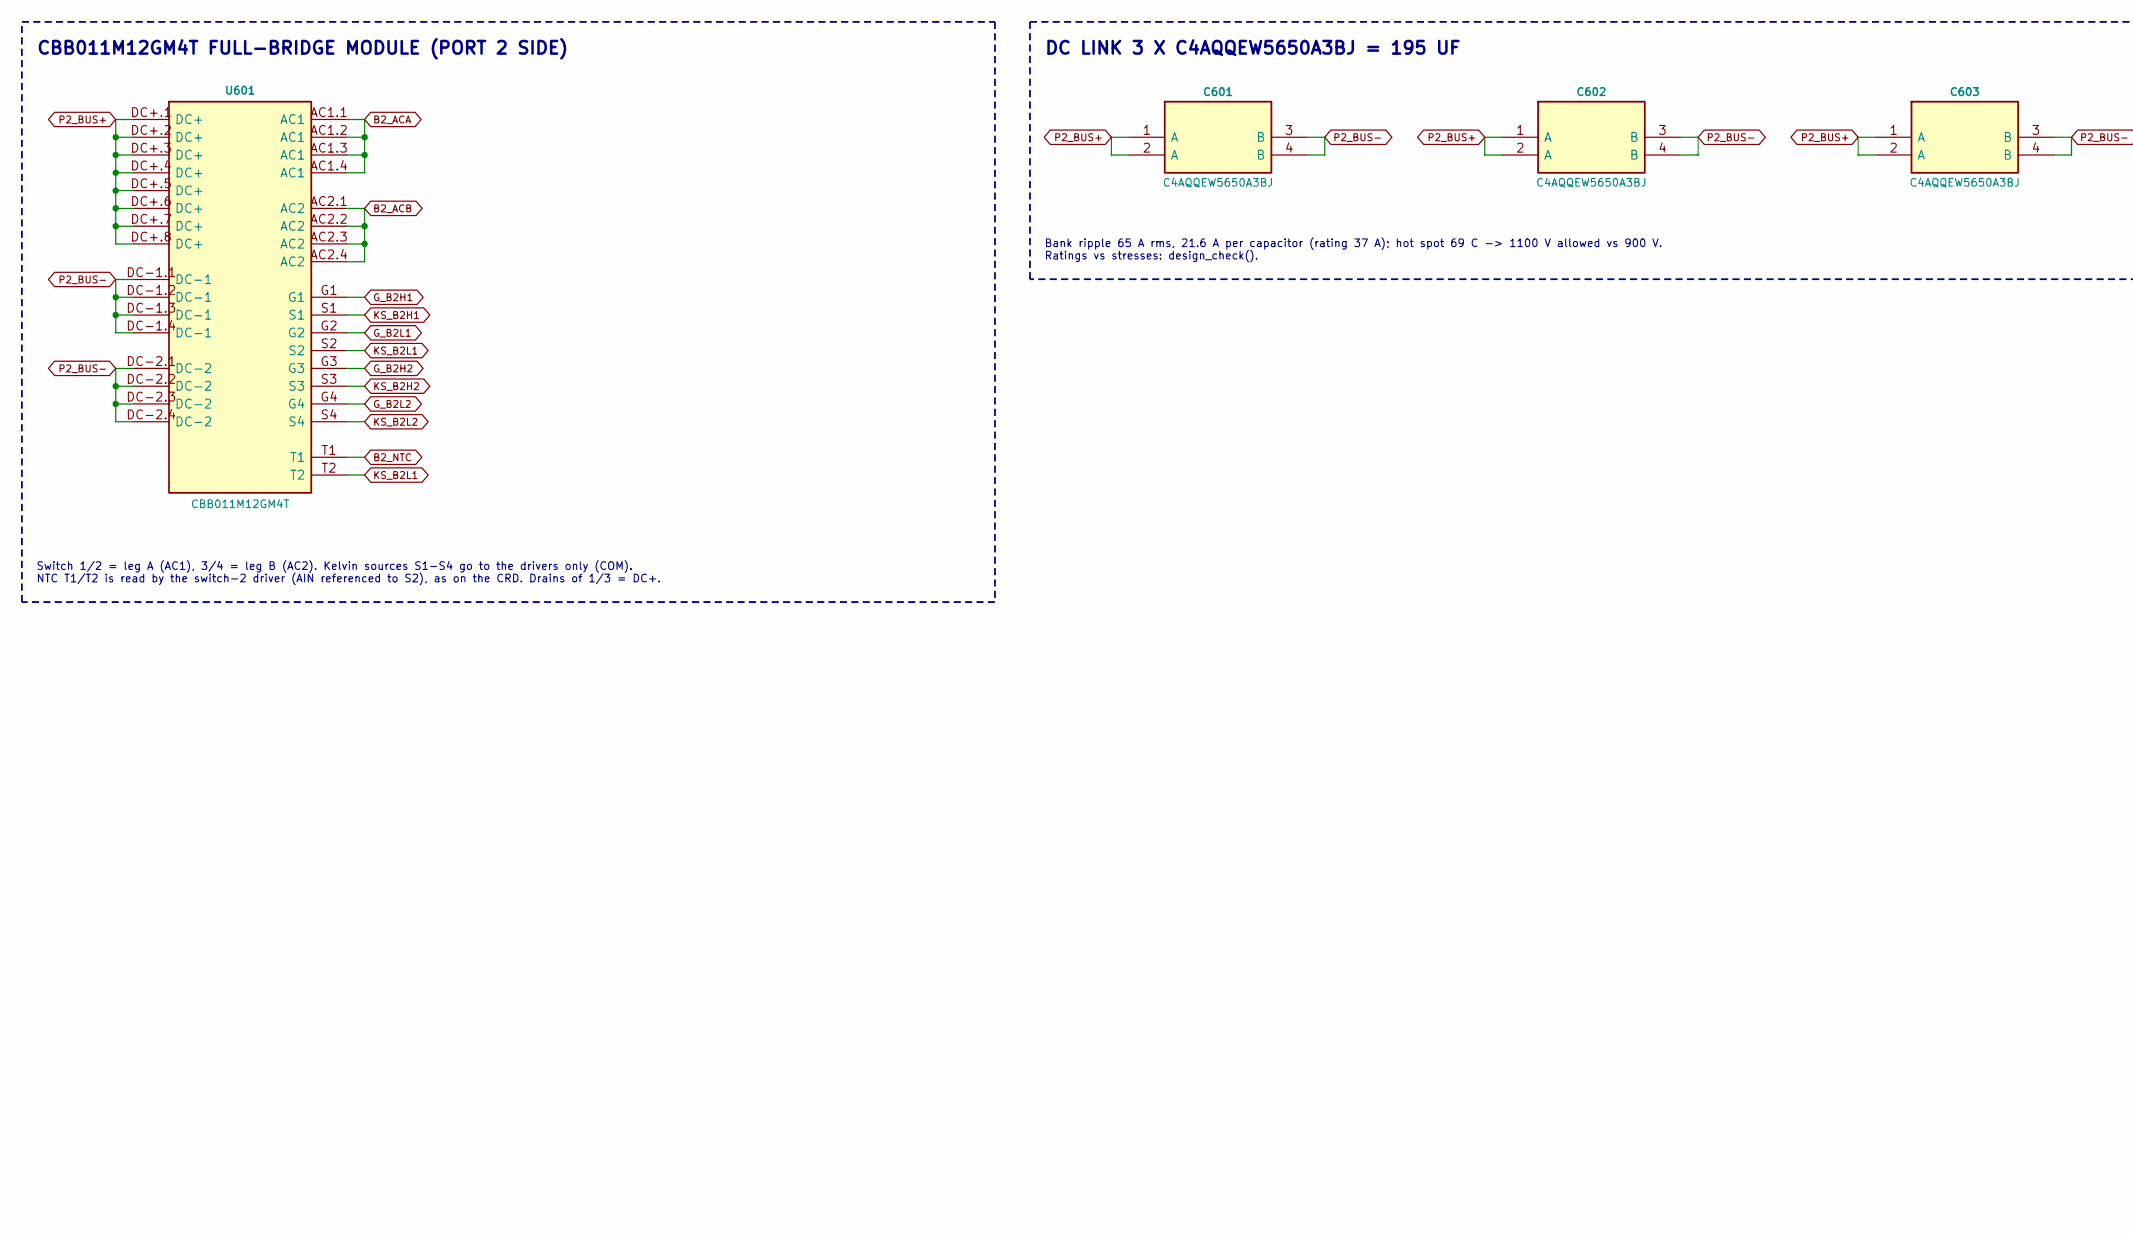
[picture p228: schematic 06_b2_power.kicad_sch, part in row 1, column 1]

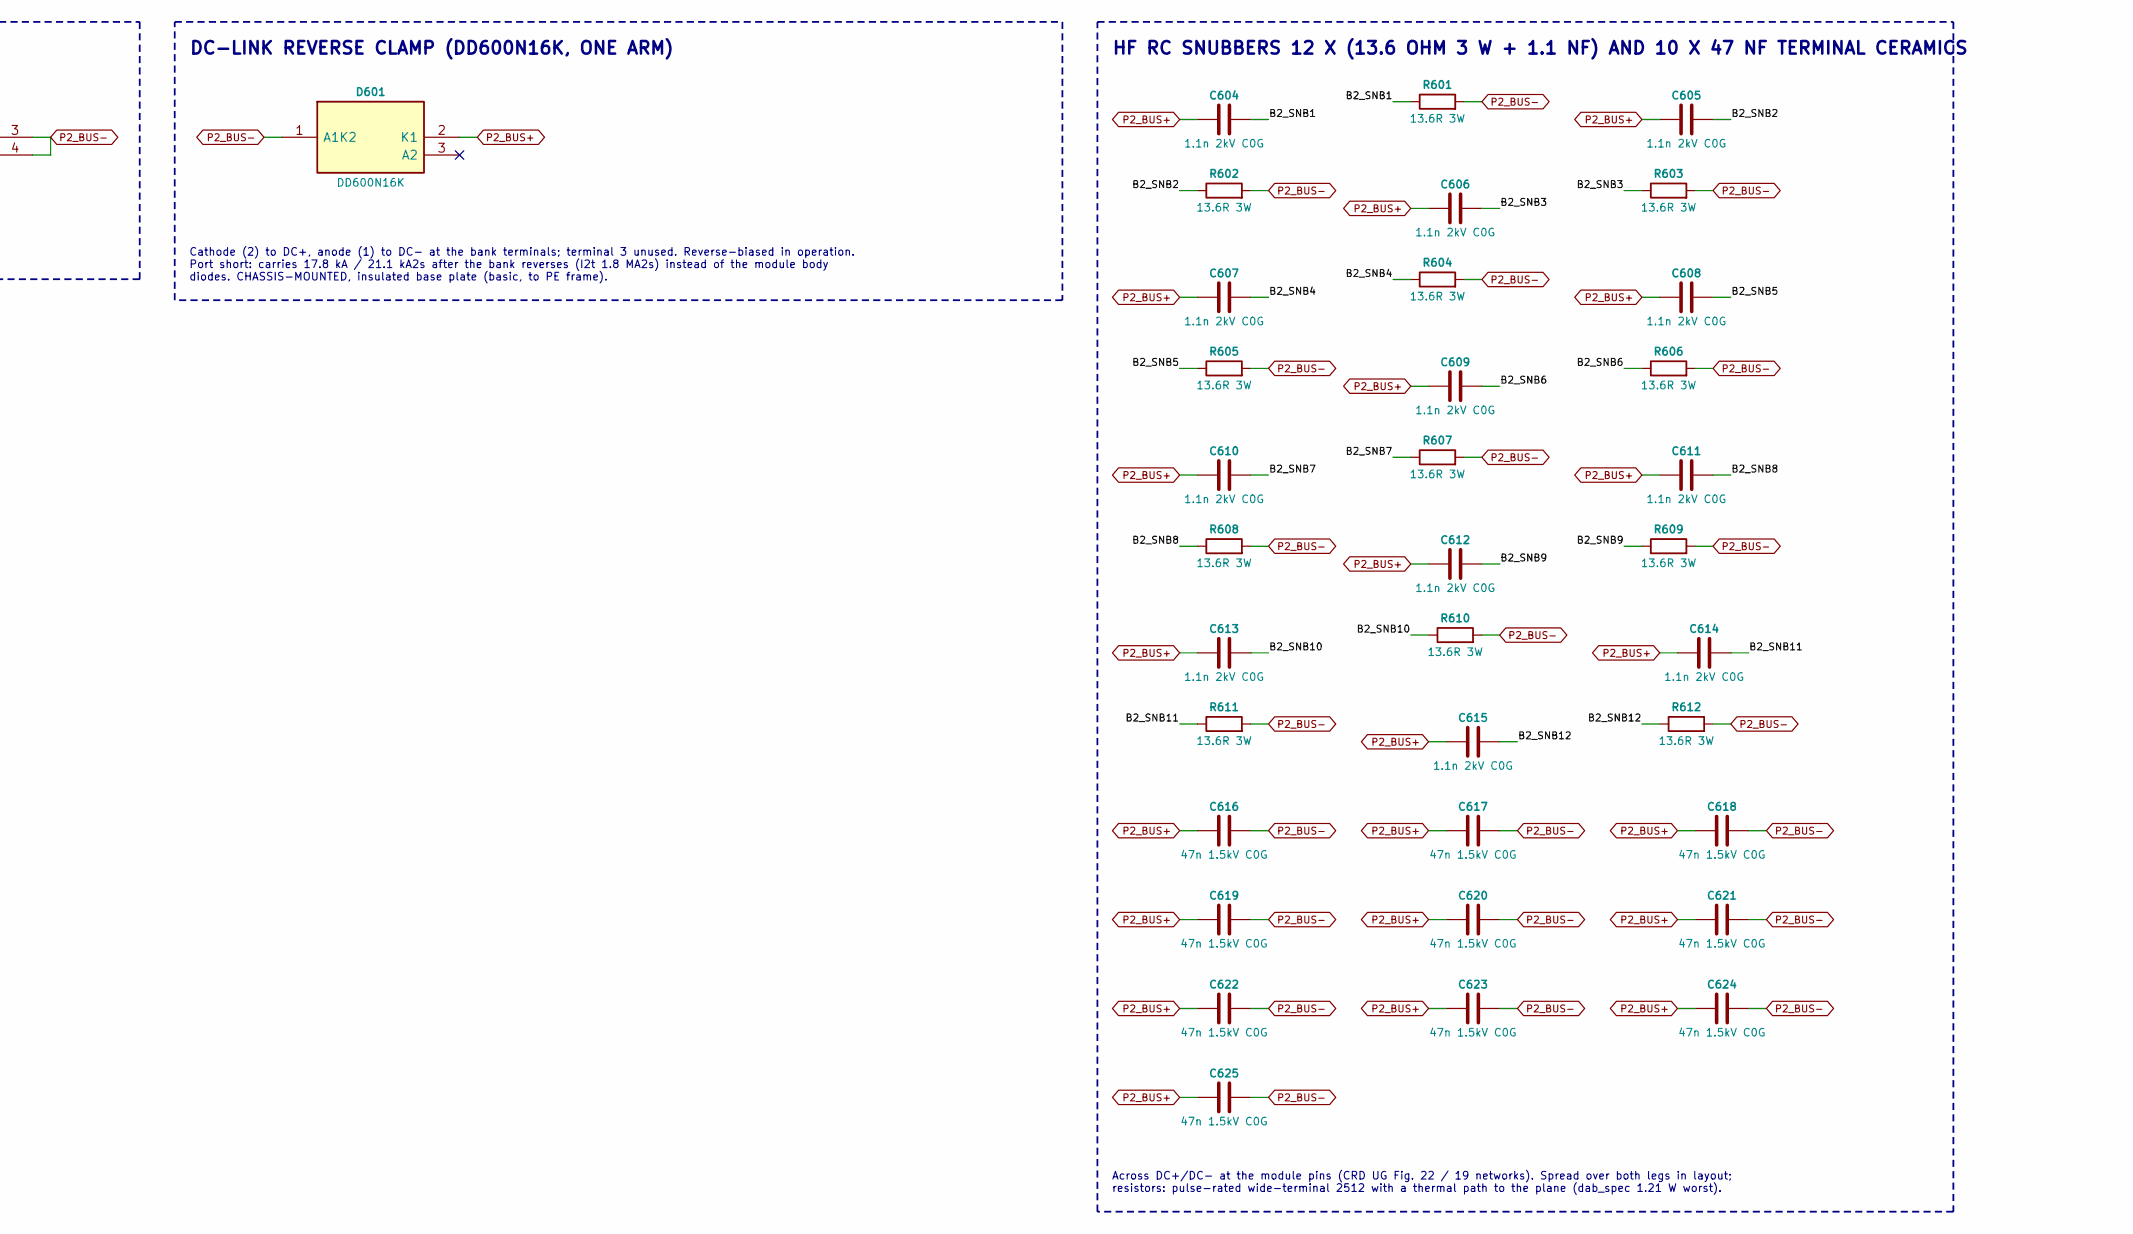
[picture p229: schematic 06_b2_power.kicad_sch, part in row 1, column 2]

Parts:
C601, C602, C603: C4AQQEW5650A3BJ; MPN C4AQQEW5650A3BJ
C604, C605, C606, C607, C608, C609, C610, C611, C612, C613, C614, C615: 1.1n 2kV C0G
C616, C617, C618, C619, C620, C621, C622, C623, C624, C625: 47n 1.5kV C0G
D601: DD600N16K; MPN DD600N16K
R601, R602, R603, R604, R605, R606, R607, R608, R609, R610, R611, R612: 13.6R 3W
U601: CBB011M12GM4T; MPN CBB011M12GM4T

Connections:
B2_ACA: U601.AC1.1 (AC1), U601.AC1.2 (AC1), U601.AC1.3 (AC1), U601.AC1.4 (AC1)
B2_ACB: U601.AC2.1 (AC2), U601.AC2.2 (AC2), U601.AC2.3 (AC2), U601.AC2.4 (AC2)
B2_NTC: U601.T1
B2_SNB1: C604.2, R601.1
B2_SNB2: C605.2, R602.1
B2_SNB3: C606.2, R603.1
B2_SNB4: C607.2, R604.1
B2_SNB5: C608.2, R605.1
B2_SNB6: C609.2, R606.1
B2_SNB7: C610.2, R607.1
B2_SNB8: C611.2, R608.1
B2_SNB9: C612.2, R609.1
B2_SNB10: C613.2, R610.1
B2_SNB11: C614.2, R611.1
B2_SNB12: C615.2, R612.1
G_B2H1: U601.G1
G_B2H2: U601.G3
G_B2L1: U601.G2
G_B2L2: U601.G4
KS_B2H1: U601.S1
KS_B2H2: U601.S3
KS_B2L1: U601.S2, U601.T2
KS_B2L2: U601.S4
P2_BUS+: C601.1 (A), C601.2 (A), C602.1 (A), C602.2 (A), C603.1 (A), C603.2 (A), C604.1, C605.1, C606.1, C607.1, C608.1, C609.1, C610.1, C611.1, C612.1, C613.1, C614.1, C615.1, C616.1, C617.1, C618.1, C619.1, C620.1, C621.1, C622.1, C623.1, C624.1, C625.1, D601.2 (K1), U601.DC+.1 (DC+), U601.DC+.2 (DC+), U601.DC+.3 (DC+), U601.DC+.4 (DC+), U601.DC+.5 (DC+), U601.DC+.6 (DC+), U601.DC+.7 (DC+), U601.DC+.8 (DC+)
P2_BUS-: C601.3 (B), C601.4 (B), C602.3 (B), C602.4 (B), C603.3 (B), C603.4 (B), C616.2, C617.2, C618.2, C619.2, C620.2, C621.2, C622.2, C623.2, C624.2, C625.2, D601.1 (A1K2), R601.2, R602.2, R603.2, R604.2, R605.2, R606.2, R607.2, R608.2, R609.2, R610.2, R611.2, R612.2, U601.DC-1.1 (DC-1), U601.DC-1.2 (DC-1), U601.DC-1.3 (DC-1), U601.DC-1.4 (DC-1), U601.DC-2.1 (DC-2), U601.DC-2.2 (DC-2), U601.DC-2.3 (DC-2), U601.DC-2.4 (DC-2)

Notes on the sheet:
HF RC SNUBBERS 12 X (13.6 OHM 3 W + 1.1 NF) AND 10 X 47 NF TERMINAL CERAMICS
DC-LINK REVERSE CLAMP (DD600N16K, ONE ARM)
Bank ripple 65 A rms, 21.6 A per capacitor (rating 37 A); hot spot 69 C -> 1100 V allowed vs 900 V. Ratings vs stresses: design_check().
DC LINK 3 X C4AQQEW5650A3BJ = 195 UF
Across DC+/DC- at the module pins (CRD UG Fig. 22 / 19 networks). Spread over both legs in layout; resistors: pulse-rated wide-terminal 2512 with a thermal path to the plane (dab_spec 1.21 W worst).
CBB011M12GM4T FULL-BRIDGE MODULE (PORT 2 SIDE)
Cathode (2) to DC+, anode (1) to DC- at the bank terminals; terminal 3 unused. Reverse-biased in operation. Port short: carries 17.8 kA / 21.1 kA2s after the bank reverses (I2t 1.8 MA2s) instead of the module body diodes. CHASSIS-MOUNTED, insulated base plate (basic, to PE frame).
Switch 1/2 = leg A (AC1), 3/4 = leg B (AC2). Kelvin sources S1-S4 go to the drivers only (COM). NTC T1/T2 is read by the switch-2 driver (AIN referenced to S2), as on the CRD. Drains of 1/3 = DC+.
