vectivolt/PCM/hardware/DAB60/sheets/07_b2_gatea.kicad_sch

## KiCad design hardware/DAB60/sheets/07_b2_gatea.kicad_sch (2026-10-04)

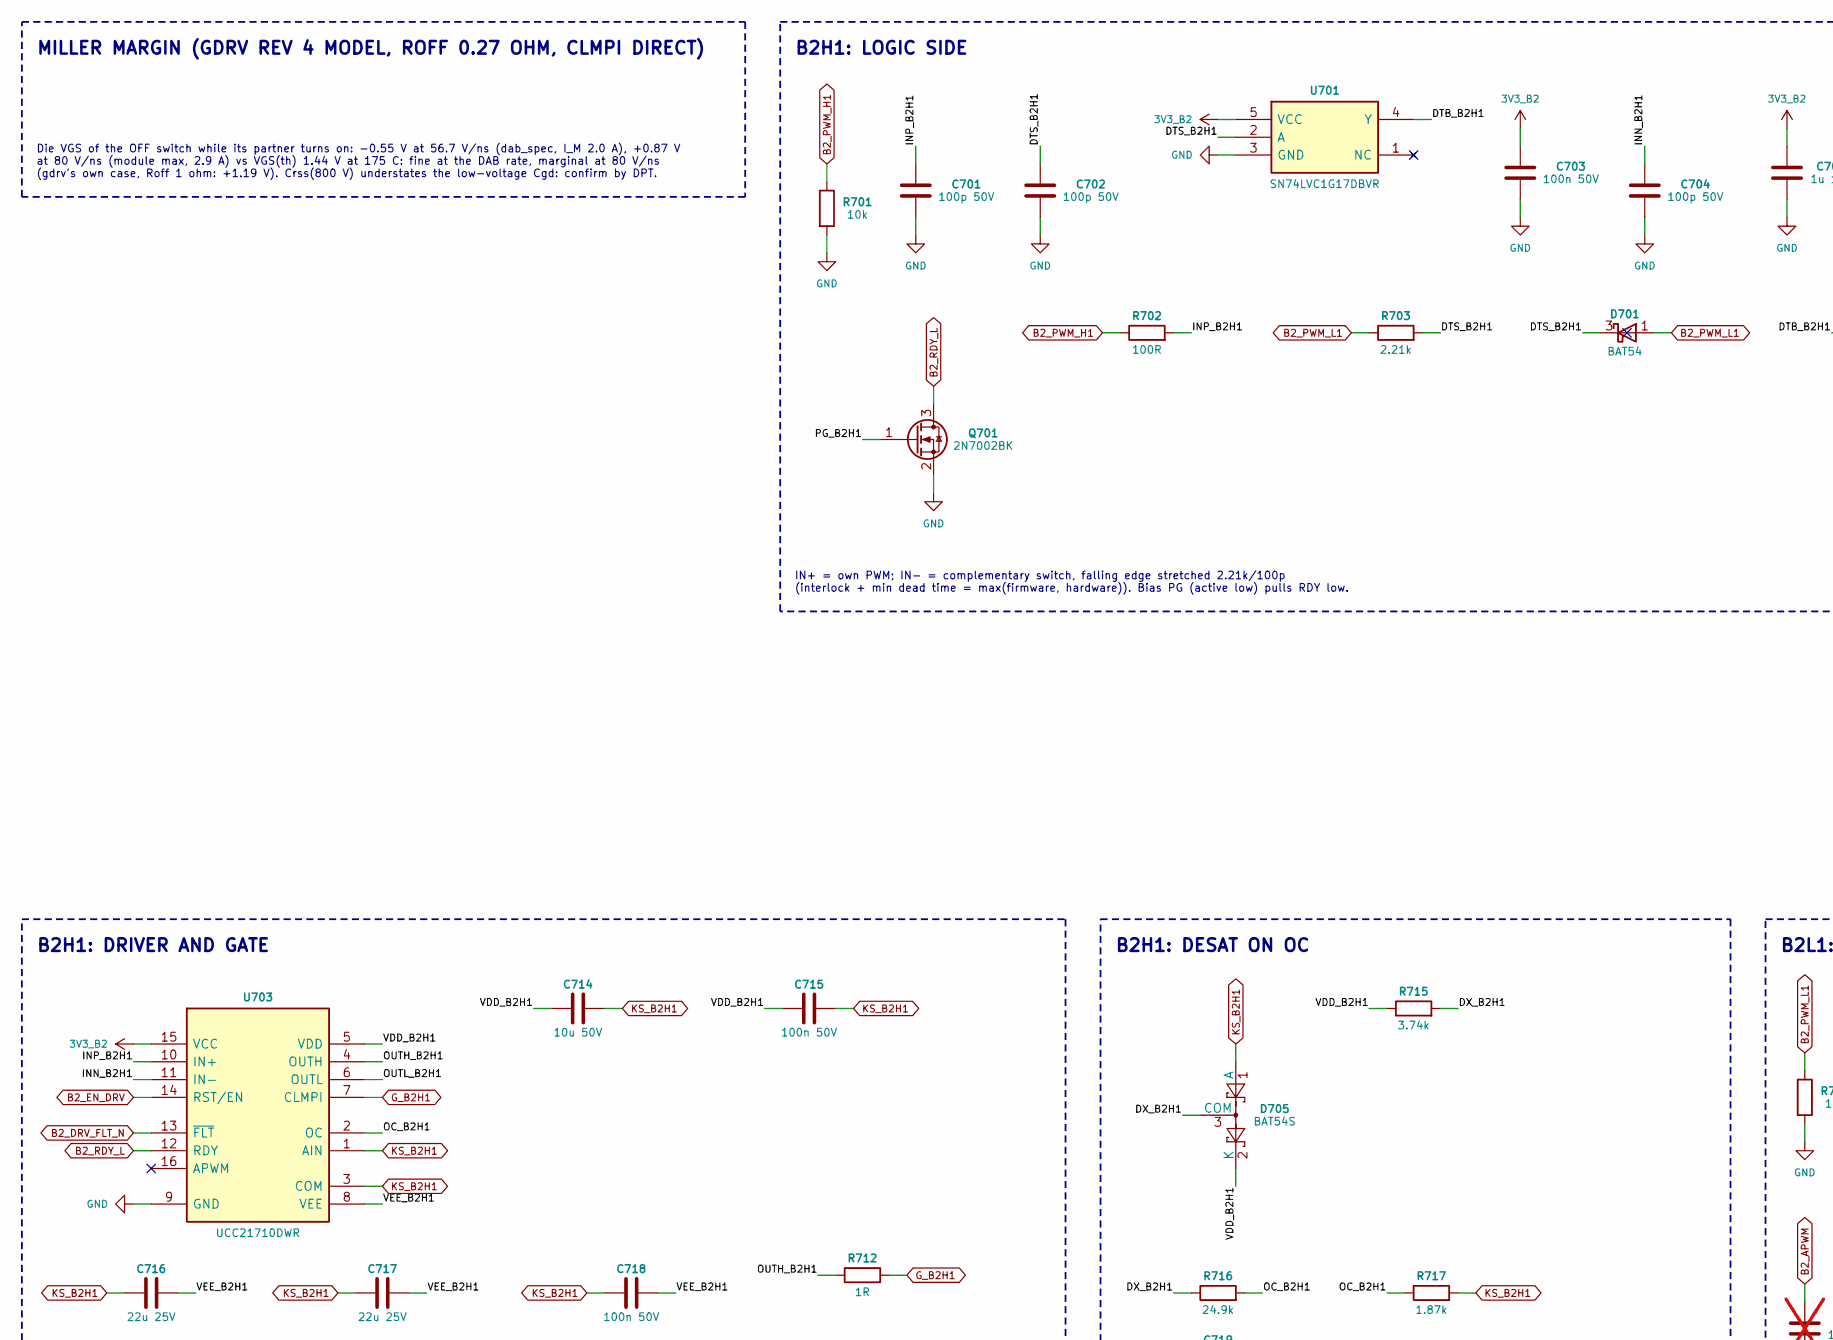
[picture p230: schematic 07_b2_gatea.kicad_sch, part in row 1, column 1]

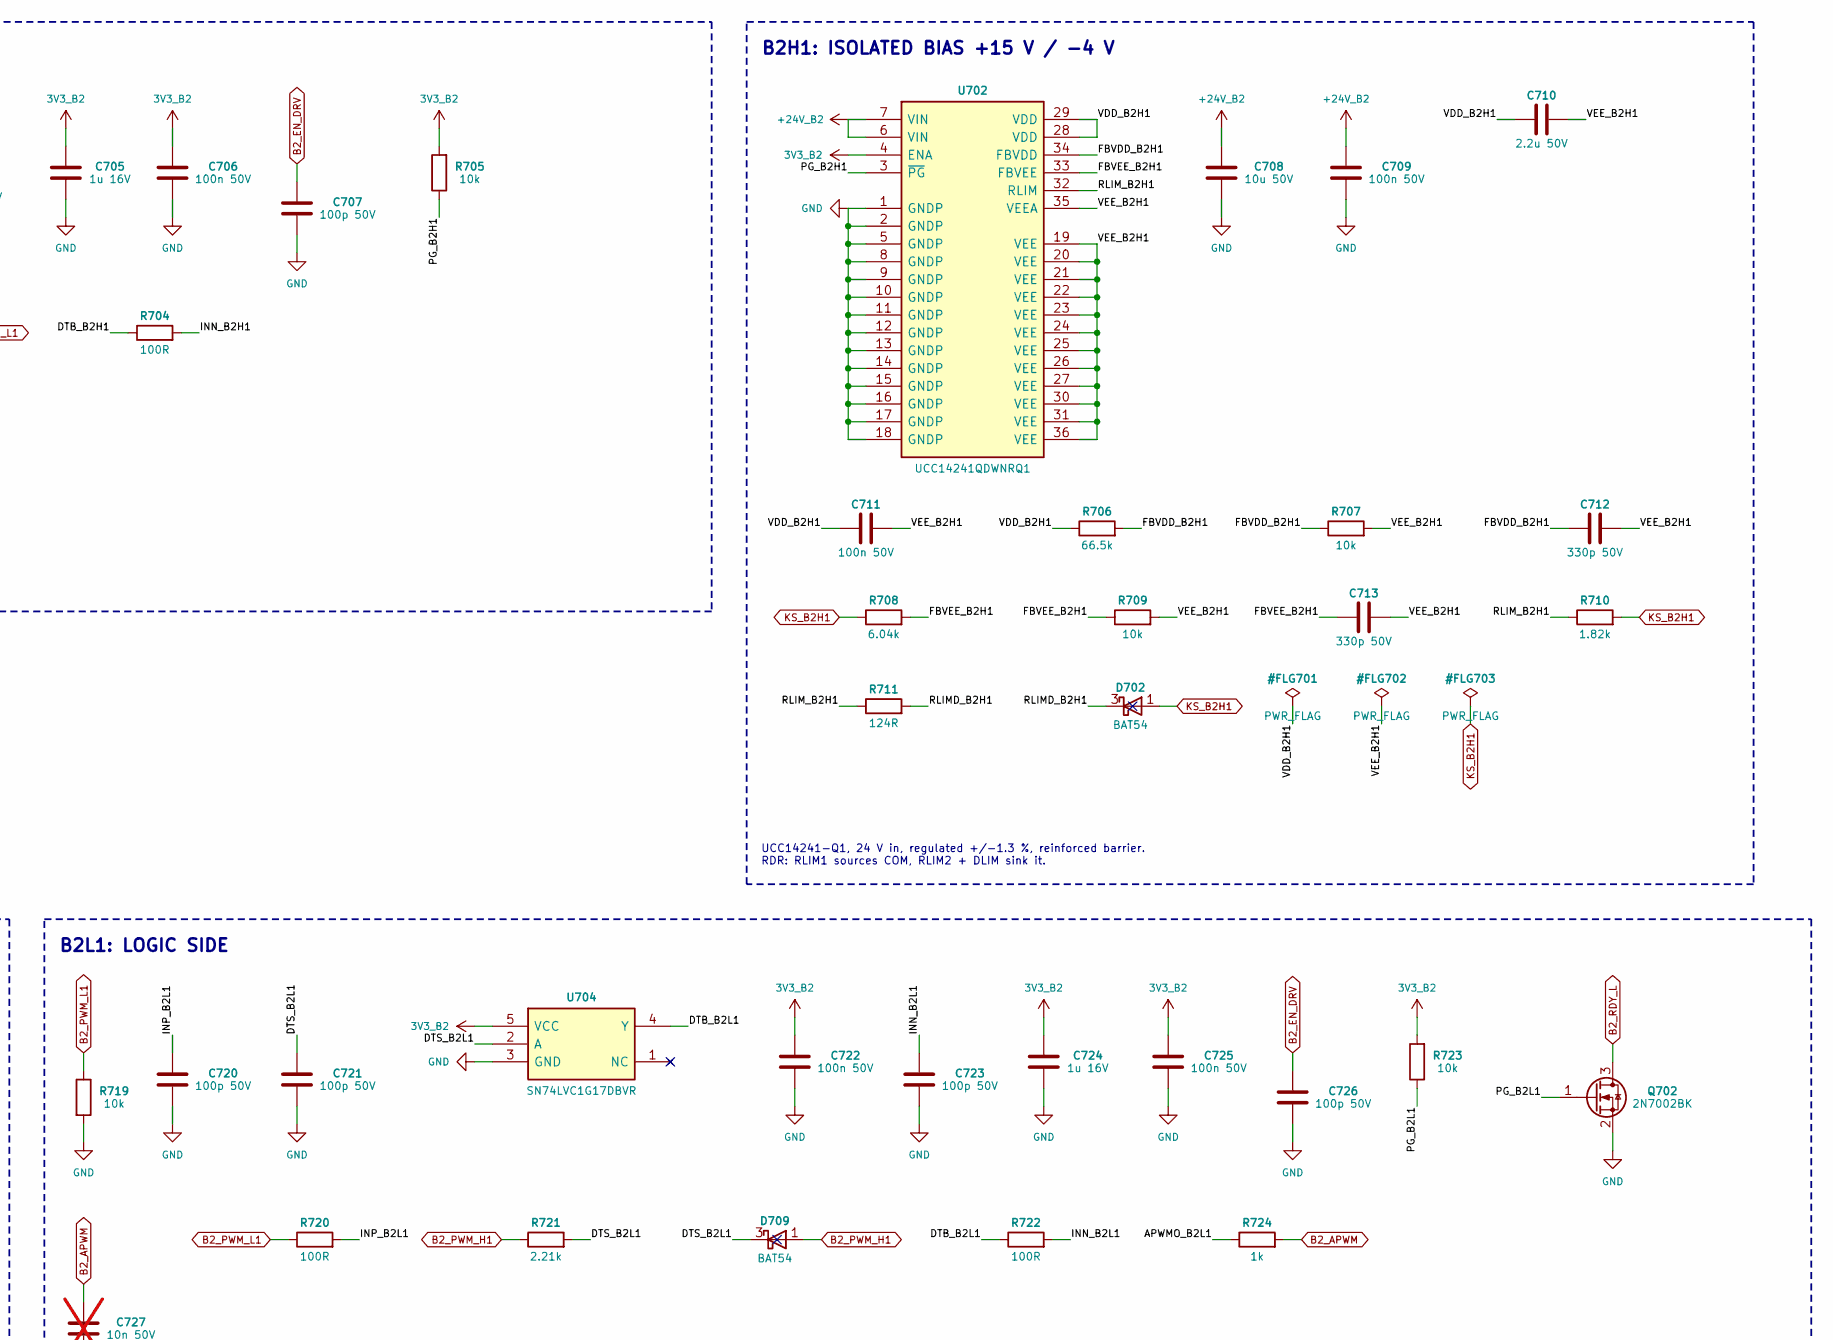
[picture p231: schematic 07_b2_gatea.kicad_sch, part in row 1, column 2]

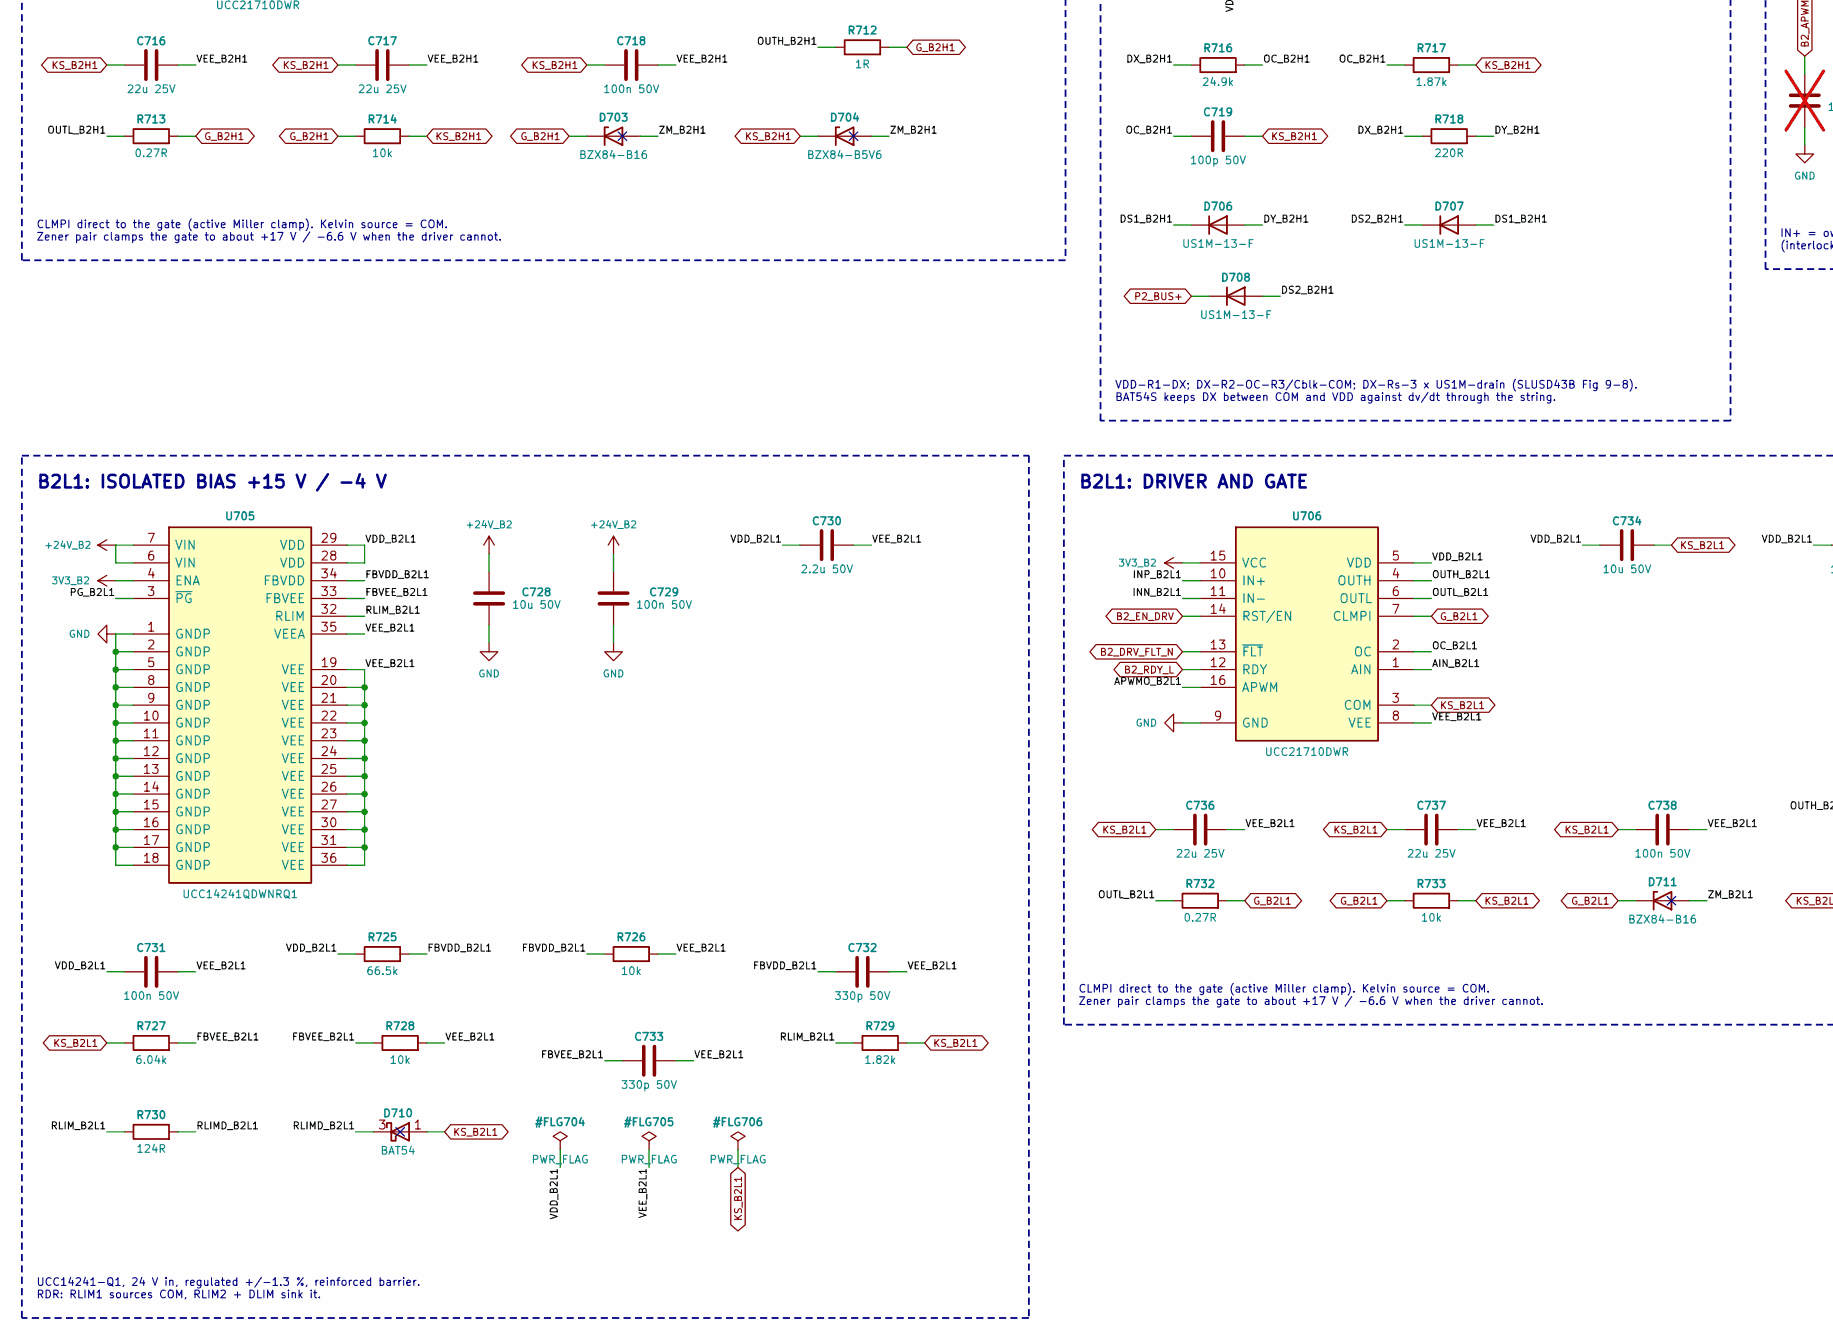
[picture p232: schematic 07_b2_gatea.kicad_sch, part in row 2, column 1]

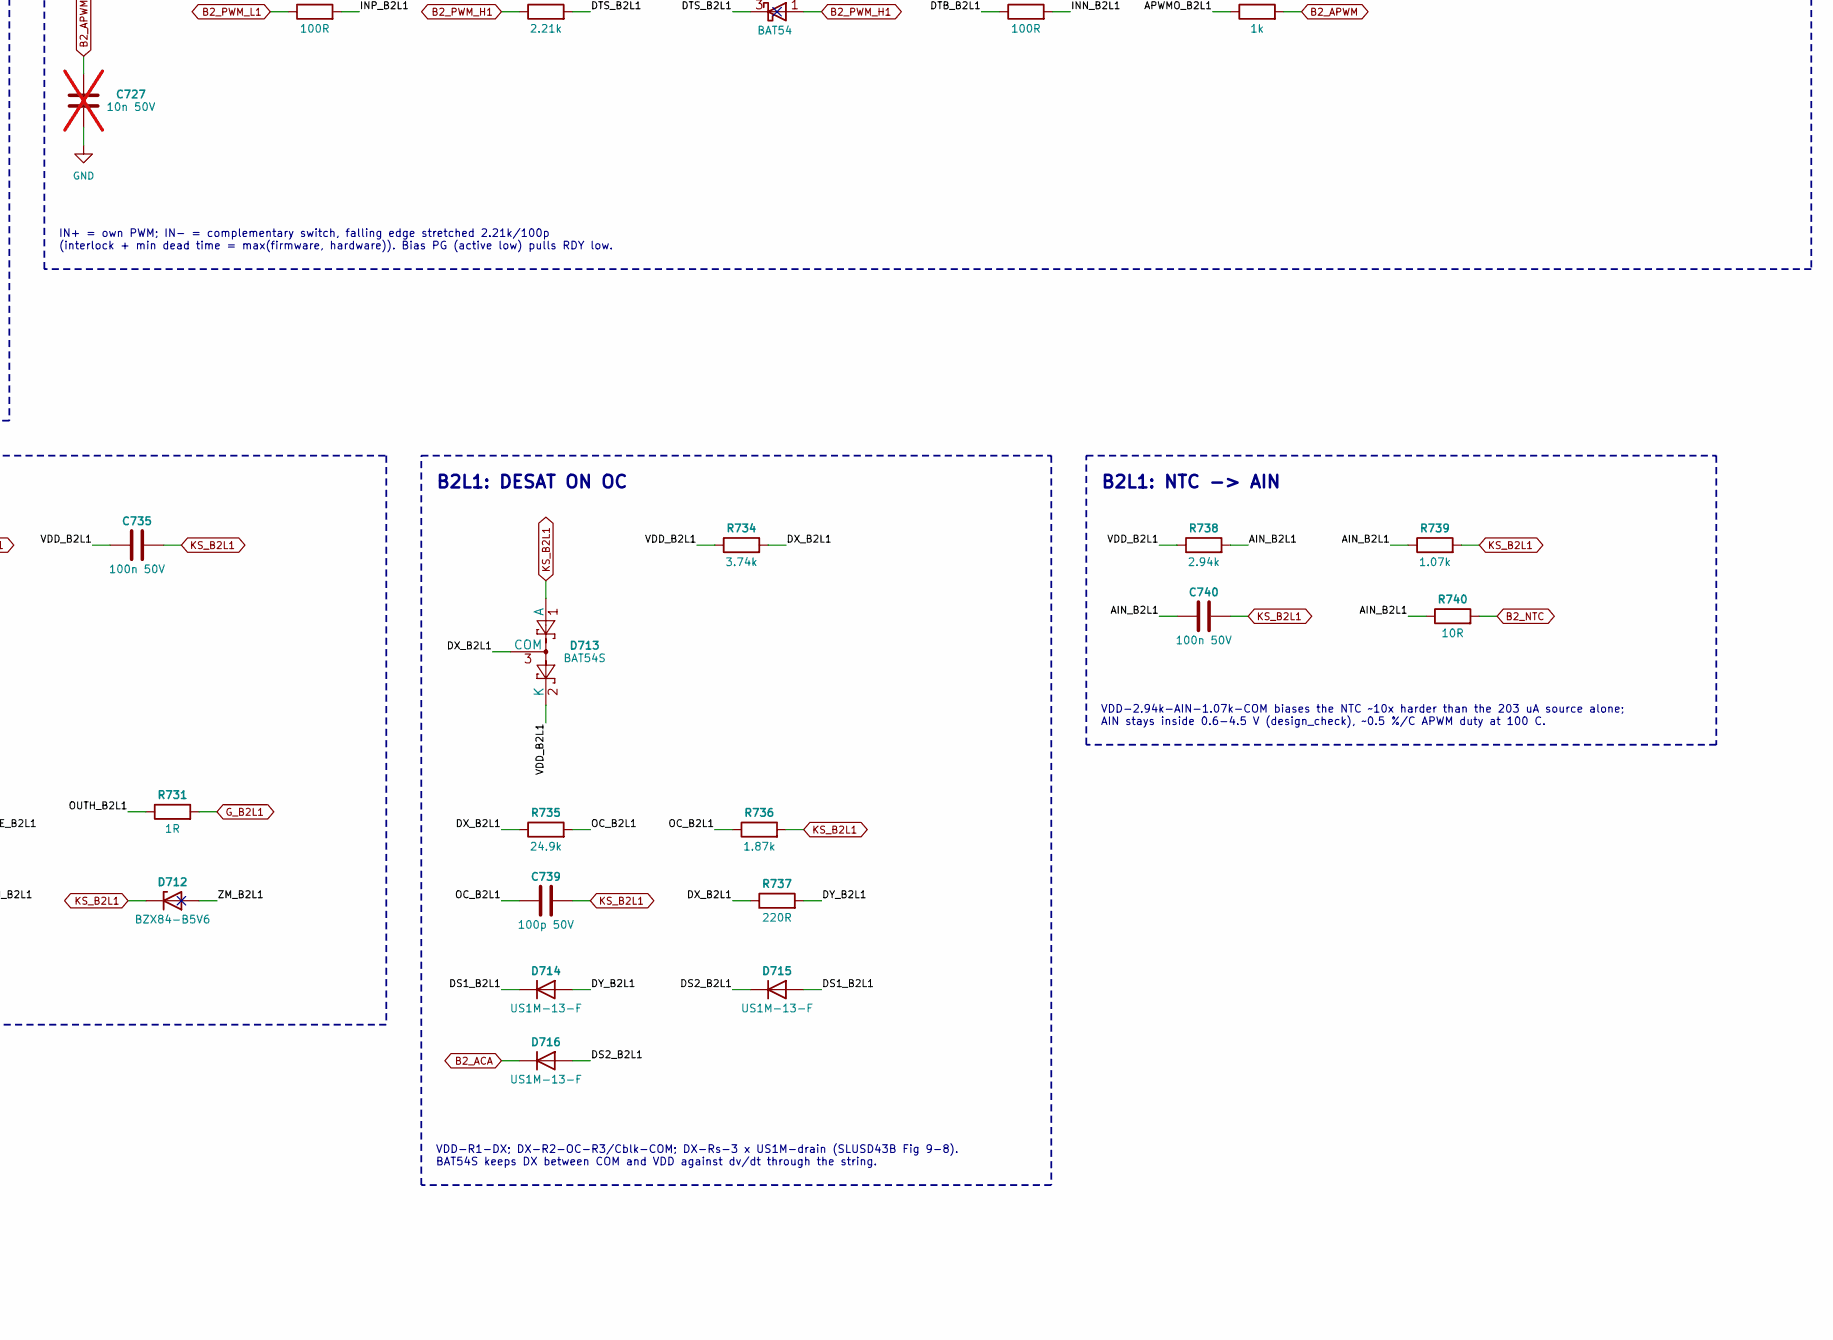
[picture p233: schematic 07_b2_gatea.kicad_sch, part in row 2, column 2]

Parts:
C701, C702, C704, C707, C719, C720, C721, C723, C726, C739: 100p 50V
C703, C706, C709, C711, C715, C718, C722, C725, C729, C731, C735, C738, C740: 100n 50V
C705, C724: 1u 16V
C708, C714, C728, C734: 10u 50V
C710, C730: 2.2u 50V
C712, C713, C732, C733: 330p 50V
C716, C717, C736, C737: 22u 25V
C727: 10n 50V; not fitted
D701, D702, D709, D710: BAT54; MPN BAT54
D703, D711: BZX84-B16; MPN BZX84-B16
D704, D712: BZX84-B5V6; MPN BZX84-B5V6
D705, D713: BAT54S; MPN BAT54S
D706, D707, D708, D714, D715, D716: US1M-13-F; MPN US1M-13-F
Q701, Q702: 2N7002BK; MPN 2N7002BK
R701, R705, R707, R709, R714, R719, R723, R726, R728, R733: 10k
R702, R704, R720, R722: 100R
R703, R721: 2.21k
R706, R725: 66.5k
R708, R727: 6.04k
R710, R729: 1.82k
R711, R730: 124R
R712, R731: 1R
R713, R732: 0.27R
R715, R734: 3.74k
R716, R735: 24.9k
R717, R736: 1.87k
R718, R737: 220R
R724: 1k
R738: 2.94k
R739: 1.07k
R740: 10R
U701, U704: SN74LVC1G17DBVR; MPN SN74LVC1G17DBVR
U702, U705: UCC14241QDWNRQ1; MPN UCC14241QDWNRQ1
U703, U706: UCC21710DWR; MPN UCC21710DWR

Connections:
3V3_B2: C703.1, C705.1, C706.1, C722.1, C724.1, C725.1, R705.2, R723.2, U701.5 (VCC), U702.4 (ENA), U703.15 (VCC), U704.5 (VCC), U705.4 (ENA), U706.15 (VCC)
+24V_B2: C708.1, C709.1, C728.1, C729.1, U702.6 (VIN), U702.7 (VIN), U705.6 (VIN), U705.7 (VIN)
AIN_B2L1: C740.1, R738.2, R739.1, R740.1, U706.1 (AIN)
APWMO_B2L1: R724.1, U706.16 (APWM)
B2_ACA: D716.1 (K)
B2_APWM: C727.1, R724.2
B2_DRV_FLT_N: U703.13 (~FLT), U706.13 (~FLT)
B2_EN_DRV: C707.1, C726.1, U703.14 (RST/EN), U706.14 (RST/EN)
B2_NTC: R740.2
B2_PWM_H1: D709.1 (A), R701.1, R702.1, R721.1
B2_PWM_L1: D701.1 (A), R703.1, R719.1, R720.1
B2_RDY_L: Q701.3 (D), Q702.3 (D), U703.12 (RDY), U706.12 (RDY)
DS1_B2H1: D706.1 (K), D707.2 (A)
DS1_B2L1: D714.1 (K), D715.2 (A)
DS2_B2H1: D707.1 (K), D708.2 (A)
DS2_B2L1: D715.1 (K), D716.2 (A)
DTB_B2H1: R704.1, U701.4 (Y)
DTB_B2L1: R722.1, U704.4 (Y)
DTS_B2H1: C702.1, D701.3 (K), R703.2, U701.2 (A)
DTS_B2L1: C721.1, D709.3 (K), R721.2, U704.2 (A)
DX_B2H1: D705.3 (COM), R715.2, R716.1, R718.1
DX_B2L1: D713.3 (COM), R734.2, R735.1, R737.1
DY_B2H1: D706.2 (A), R718.2
DY_B2L1: D714.2 (A), R737.2
FBVDD_B2H1: C712.1, R706.2, R707.1, U702.34 (FBVDD)
FBVDD_B2L1: C732.1, R725.2, R726.1, U705.34 (FBVDD)
FBVEE_B2H1: C713.1, R708.2, R709.1, U702.33 (FBVEE)
FBVEE_B2L1: C733.1, R727.2, R728.1, U705.33 (FBVEE)
GND: C701.2, C702.2, C703.2, C704.2, C705.2, C706.2, C707.2, C708.2, C709.2, C720.2, C721.2, C722.2, C723.2, C724.2, C725.2, C726.2, C727.2, C728.2, C729.2, Q701.2 (S), Q702.2 (S), R701.2, R719.2, U701.3 (GND), U702.1 (GNDP), U702.2 (GNDP), U702.5 (GNDP), U702.8 (GNDP), U702.9 (GNDP), U702.10 (GNDP), U702.11 (GNDP), U702.12 (GNDP), U702.13 (GNDP), U702.14 (GNDP), U702.15 (GNDP), U702.16 (GNDP), U702.17 (GNDP), U702.18 (GNDP), U703.9 (GND), U704.3 (GND), U705.1 (GNDP), U705.2 (GNDP), U705.5 (GNDP), U705.8 (GNDP), U705.9 (GNDP), U705.10 (GNDP), U705.11 (GNDP), U705.12 (GNDP), U705.13 (GNDP), U705.14 (GNDP), U705.15 (GNDP), U705.16 (GNDP), U705.17 (GNDP), U705.18 (GNDP), U706.9 (GND)
G_B2H1: D703.3 (K), R712.2, R713.2, R714.1, U703.7 (CLMPI)
G_B2L1: D711.3 (K), R731.2, R732.2, R733.1, U706.7 (CLMPI)
INN_B2H1: C704.1, R704.2, U703.11 (IN-)
INN_B2L1: C723.1, R722.2, U706.11 (IN-)
INP_B2H1: C701.1, R702.2, U703.10 (IN+)
INP_B2L1: C720.1, R720.2, U706.10 (IN+)
KS_B2H1: C714.2, C715.2, C716.1, C717.1, C718.1, C719.2, D702.1 (A), D704.3 (K), D705.1 (A), R708.1, R710.2, R714.2, R717.2, U703.1 (AIN), U703.3 (COM)
KS_B2L1: C734.2, C735.2, C736.1, C737.1, C738.1, C739.2, C740.2, D710.1 (A), D712.3 (K), D713.1 (A), R727.1, R729.2, R733.2, R736.2, R739.2, U706.3 (COM)
OC_B2H1: C719.1, R716.2, R717.1, U703.2 (OC)
OC_B2L1: C739.1, R735.2, R736.1, U706.2 (OC)
OUTH_B2H1: R712.1, U703.4 (OUTH)
OUTH_B2L1: R731.1, U706.4 (OUTH)
OUTL_B2H1: R713.1, U703.6 (OUTL)
OUTL_B2L1: R732.1, U706.6 (OUTL)
P2_BUS+: D708.1 (K)
PG_B2H1: Q701.1 (G), R705.1, U702.3 (~PG)
PG_B2L1: Q702.1 (G), R723.1, U705.3 (~PG)
RLIMD_B2H1: D702.3 (K), R711.2
RLIMD_B2L1: D710.3 (K), R730.2
RLIM_B2H1: R710.1, R711.1, U702.32 (RLIM)
RLIM_B2L1: R729.1, R730.1, U705.32 (RLIM)
VDD_B2H1: C710.1, C711.1, C714.1, C715.1, D705.2 (K), R706.1, R715.1, U702.28 (VDD), U702.29 (VDD), U703.5 (VDD)
VDD_B2L1: C730.1, C731.1, C734.1, C735.1, D713.2 (K), R725.1, R734.1, R738.1, U705.28 (VDD), U705.29 (VDD), U706.5 (VDD)
VEE_B2H1: C710.2, C711.2, C712.2, C713.2, C716.2, C717.2, C718.2, R707.2, R709.2, U702.19 (VEE), U702.20 (VEE), U702.21 (VEE), U702.22 (VEE), U702.23 (VEE), U702.24 (VEE), U702.25 (VEE), U702.26 (VEE), U702.27 (VEE), U702.30 (VEE), U702.31 (VEE), U702.35 (VEEA), U702.36 (VEE), U703.8 (VEE)
VEE_B2L1: C730.2, C731.2, C732.2, C733.2, C736.2, C737.2, C738.2, R726.2, R728.2, U705.19 (VEE), U705.20 (VEE), U705.21 (VEE), U705.22 (VEE), U705.23 (VEE), U705.24 (VEE), U705.25 (VEE), U705.26 (VEE), U705.27 (VEE), U705.30 (VEE), U705.31 (VEE), U705.35 (VEEA), U705.36 (VEE), U706.8 (VEE)
ZM_B2H1: D703.1 (A), D704.1 (A)
ZM_B2L1: D711.1 (A), D712.1 (A)

Notes on the sheet:
UCC14241-Q1, 24 V in, regulated +/-1.3 %, reinforced barrier. RDR: RLIM1 sources COM, RLIM2 + DLIM sink it.
B2H1: DRIVER AND GATE
CLMPI direct to the gate (active Miller clamp). Kelvin source = COM. Zener pair clamps the gate to about +17 V / -6.6 V when the driver cannot.
B2L1: LOGIC SIDE
IN+ = own PWM; IN- = complementary switch, falling edge stretched 2.21k/100p (interlock + min dead time = max(firmware, hardware)). Bias PG (active low) pulls RDY low.
B2H1: DESAT ON OC
B2H1: ISOLATED BIAS +15 V / -4 V
VDD-R1-DX; DX-R2-OC-R3/Cblk-COM; DX-Rs-3 x US1M-drain (SLUSD43B Fig 9-8). BAT54S keeps DX between COM and VDD against dv/dt through the string.
B2H1: LOGIC SIDE
B2L1: NTC -> AIN
VDD-2.94k-AIN-1.07k-COM biases the NTC ~10x harder than the 203 uA source alone; AIN stays inside 0.6-4.5 V (design_check), ~0.5 %/C APWM duty at 100 C.
B2L1: DRIVER AND GATE
Die VGS of the OFF switch while its partner turns on: -0.55 V at 56.7 V/ns (dab_spec, I_M 2.0 A), +0.87 V at 80 V/ns (module max, 2.9 A) vs VGS(th) 1.44 V at 175 C: fine at the DAB rate, marginal at 80 V/ns (gdrv's own case, Roff 1 ohm: +1.19 V). Crss(800 V) understates the low-voltage Cgd: confirm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
B2L1: ISOLATED BIAS +15 V / -4 V
MILLER MARGIN (GDRV REV 4 MODEL, ROFF 0.27 OHM, CLMPI DIRECT)
B2L1: DESAT ON OC
