vectivolt/PCM/hardware/DAB60/sheets/08_b2_gateb.kicad_sch

## KiCad design hardware/DAB60/sheets/08_b2_gateb.kicad_sch (2026-10-04)

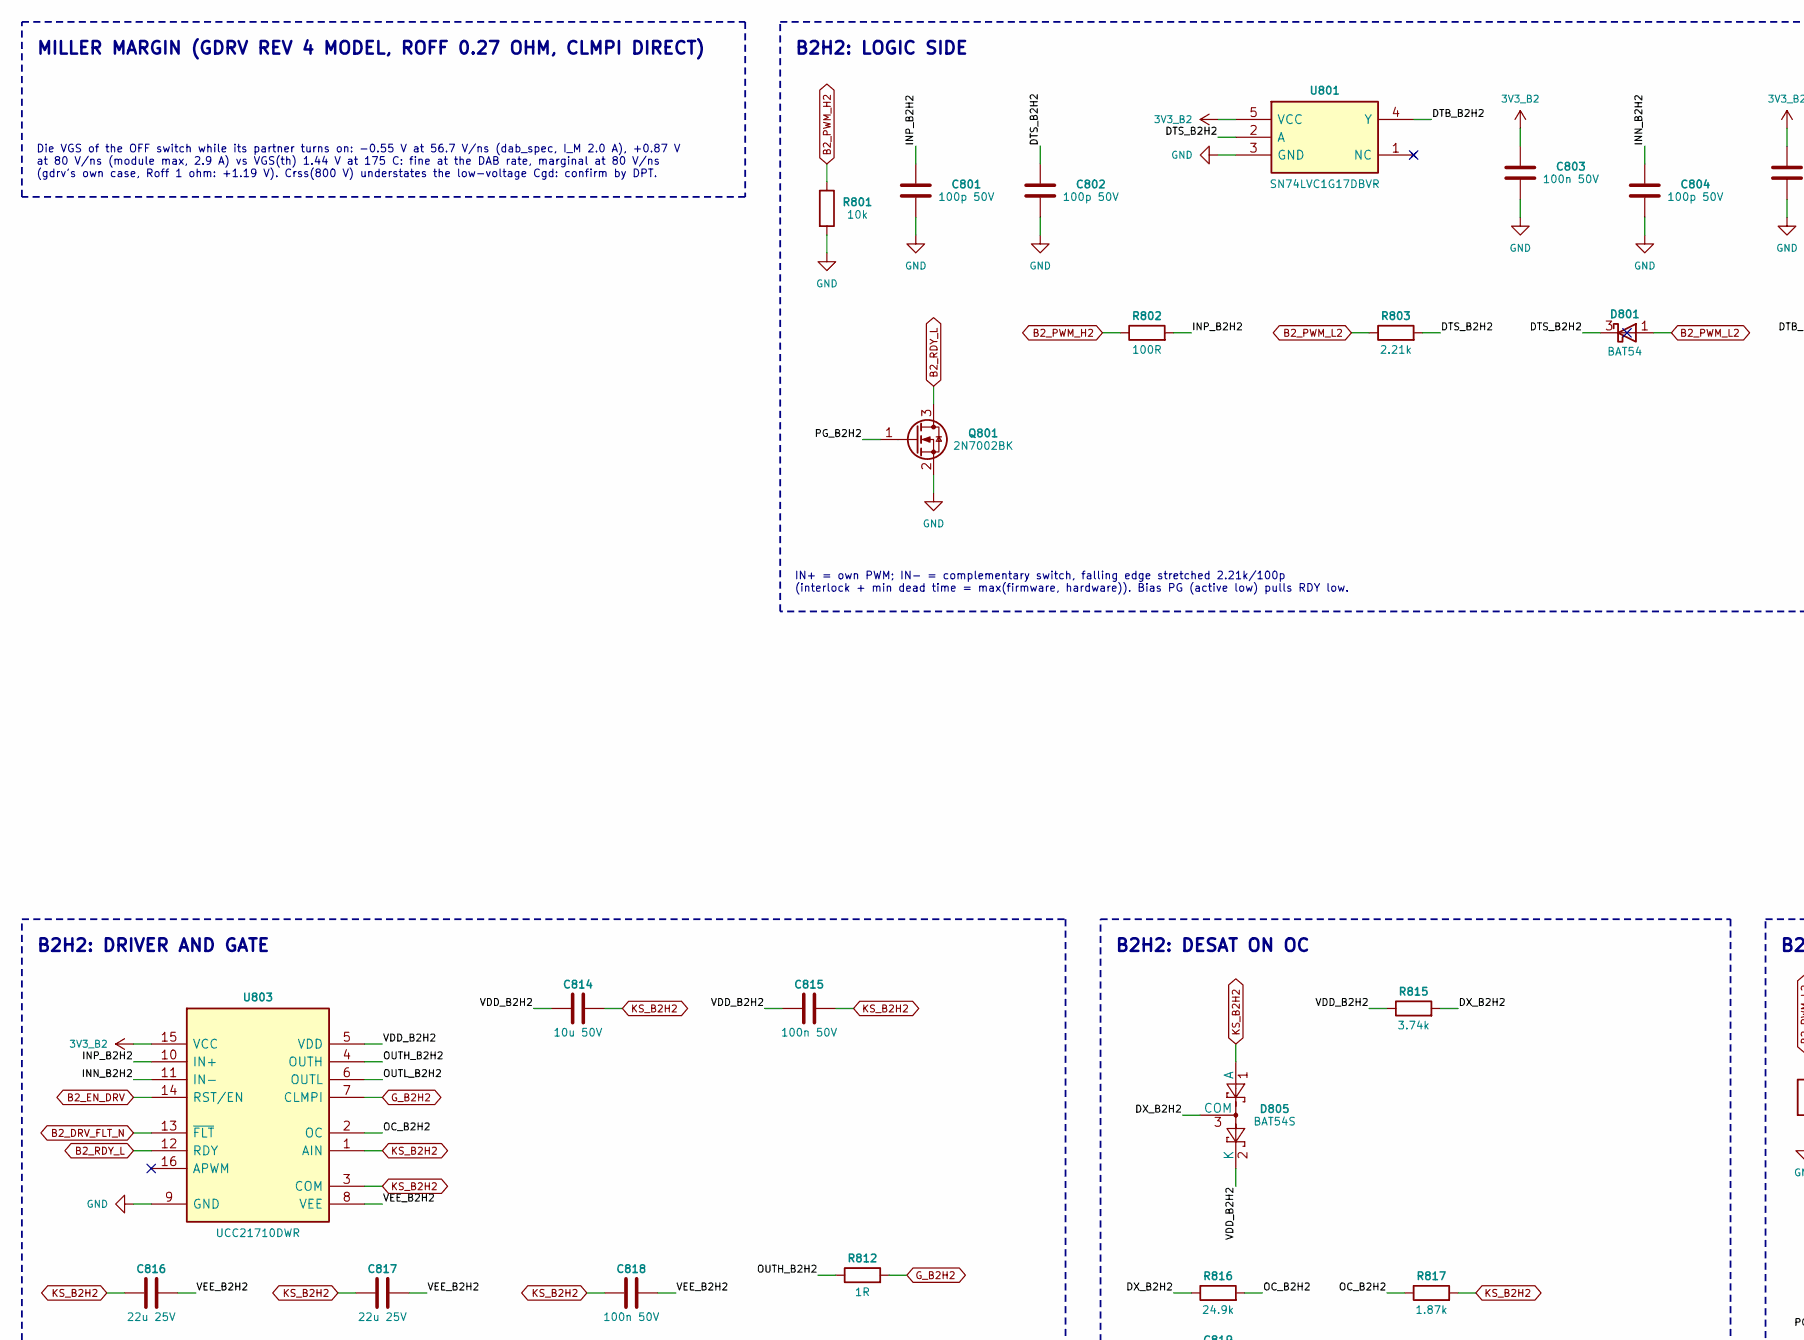
[picture p234: schematic 08_b2_gateb.kicad_sch, part in row 1, column 1]

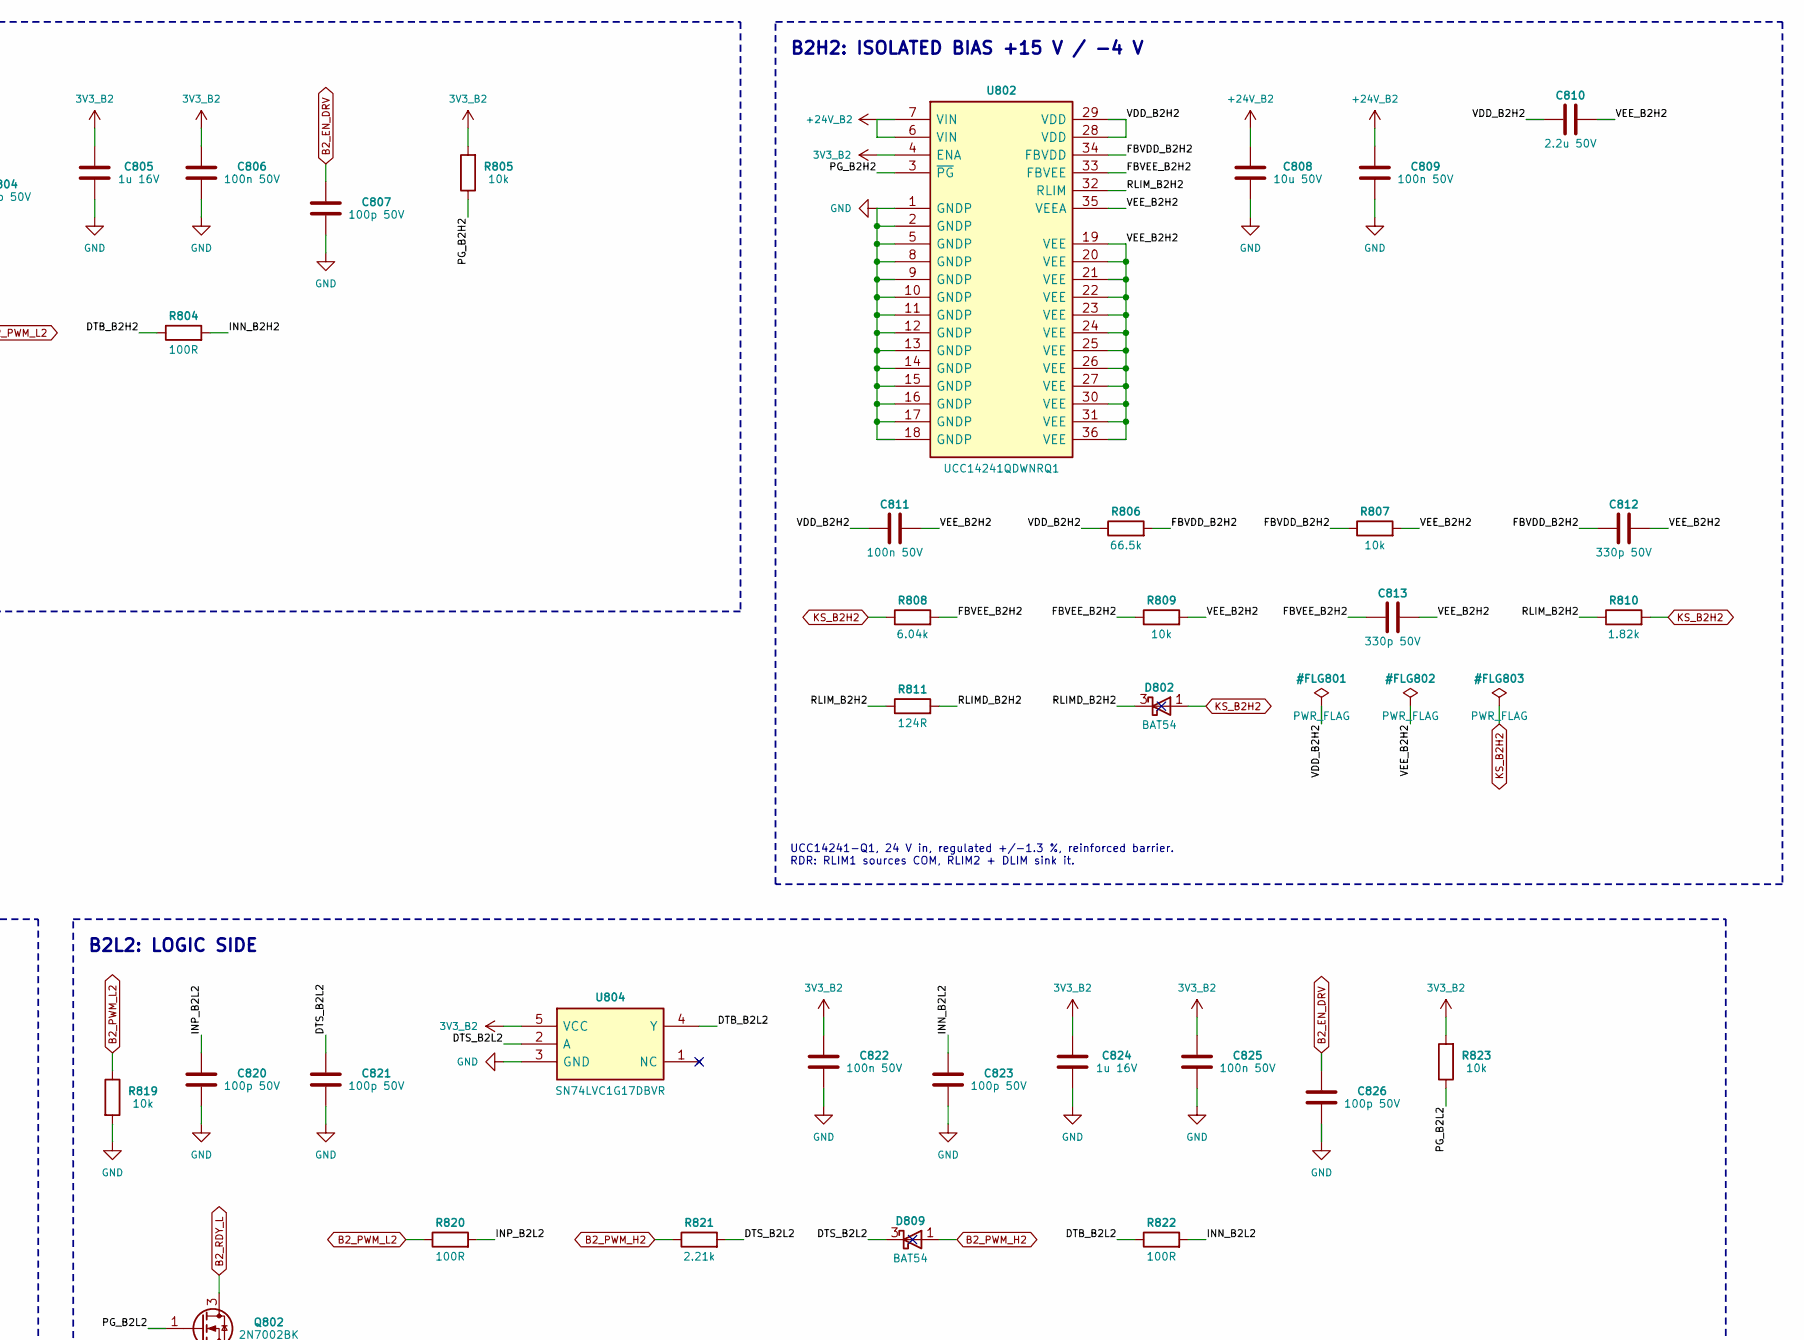
[picture p235: schematic 08_b2_gateb.kicad_sch, part in row 1, column 2]

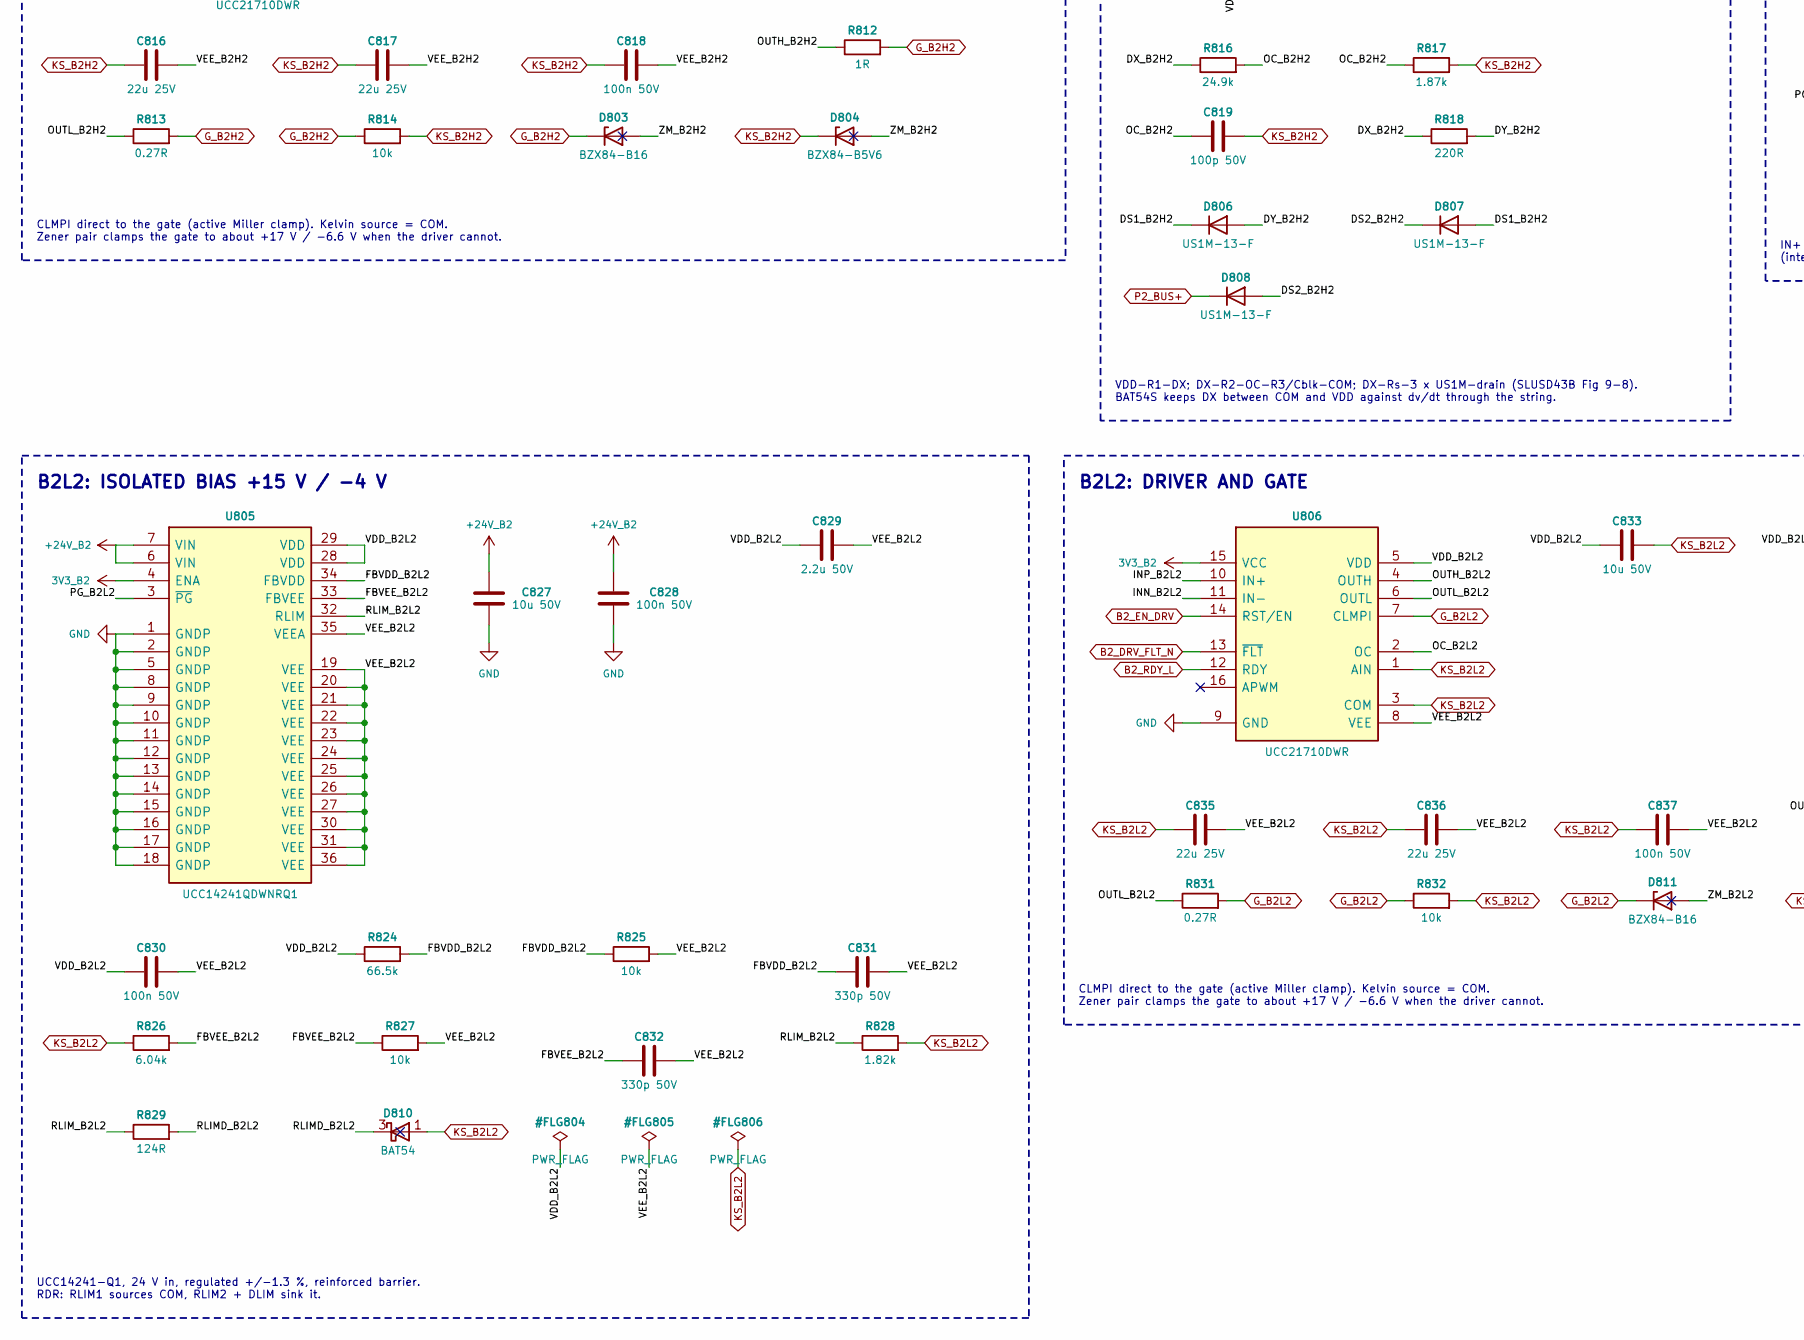
[picture p236: schematic 08_b2_gateb.kicad_sch, part in row 2, column 1]

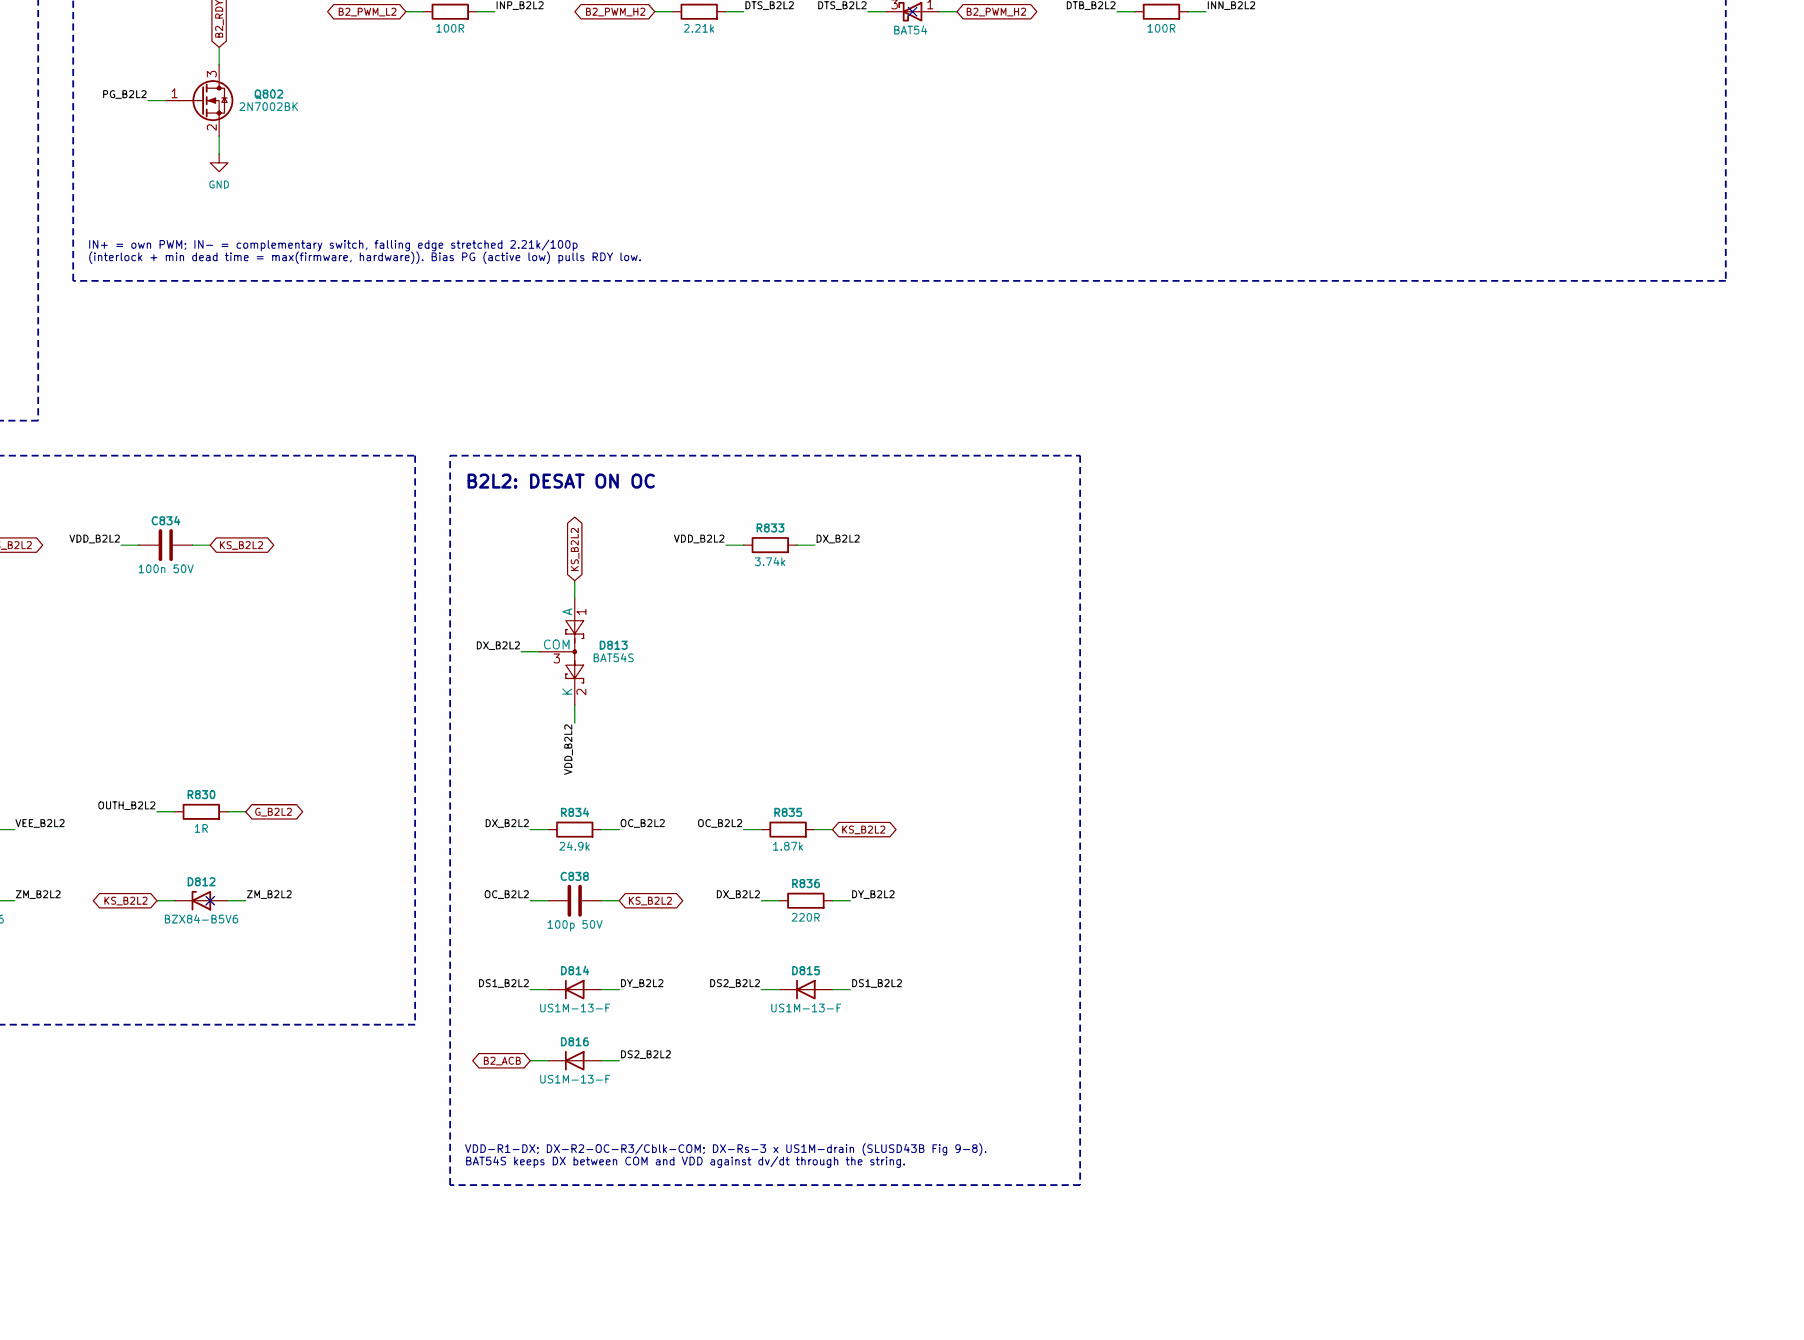
[picture p237: schematic 08_b2_gateb.kicad_sch, part in row 2, column 2]

Parts:
C801, C802, C804, C807, C819, C820, C821, C823, C826, C838: 100p 50V
C803, C806, C809, C811, C815, C818, C822, C825, C828, C830, C834, C837: 100n 50V
C805, C824: 1u 16V
C808, C814, C827, C833: 10u 50V
C810, C829: 2.2u 50V
C812, C813, C831, C832: 330p 50V
C816, C817, C835, C836: 22u 25V
D801, D802, D809, D810: BAT54; MPN BAT54
D803, D811: BZX84-B16; MPN BZX84-B16
D804, D812: BZX84-B5V6; MPN BZX84-B5V6
D805, D813: BAT54S; MPN BAT54S
D806, D807, D808, D814, D815, D816: US1M-13-F; MPN US1M-13-F
Q801, Q802: 2N7002BK; MPN 2N7002BK
R801, R805, R807, R809, R814, R819, R823, R825, R827, R832: 10k
R802, R804, R820, R822: 100R
R803, R821: 2.21k
R806, R824: 66.5k
R808, R826: 6.04k
R810, R828: 1.82k
R811, R829: 124R
R812, R830: 1R
R813, R831: 0.27R
R815, R833: 3.74k
R816, R834: 24.9k
R817, R835: 1.87k
R818, R836: 220R
U801, U804: SN74LVC1G17DBVR; MPN SN74LVC1G17DBVR
U802, U805: UCC14241QDWNRQ1; MPN UCC14241QDWNRQ1
U803, U806: UCC21710DWR; MPN UCC21710DWR

Connections:
3V3_B2: C803.1, C805.1, C806.1, C822.1, C824.1, C825.1, R805.2, R823.2, U801.5 (VCC), U802.4 (ENA), U803.15 (VCC), U804.5 (VCC), U805.4 (ENA), U806.15 (VCC)
+24V_B2: C808.1, C809.1, C827.1, C828.1, U802.6 (VIN), U802.7 (VIN), U805.6 (VIN), U805.7 (VIN)
B2_ACB: D816.1 (K)
B2_DRV_FLT_N: U803.13 (~FLT), U806.13 (~FLT)
B2_EN_DRV: C807.1, C826.1, U803.14 (RST/EN), U806.14 (RST/EN)
B2_PWM_H2: D809.1 (A), R801.1, R802.1, R821.1
B2_PWM_L2: D801.1 (A), R803.1, R819.1, R820.1
B2_RDY_L: Q801.3 (D), Q802.3 (D), U803.12 (RDY), U806.12 (RDY)
DS1_B2H2: D806.1 (K), D807.2 (A)
DS1_B2L2: D814.1 (K), D815.2 (A)
DS2_B2H2: D807.1 (K), D808.2 (A)
DS2_B2L2: D815.1 (K), D816.2 (A)
DTB_B2H2: R804.1, U801.4 (Y)
DTB_B2L2: R822.1, U804.4 (Y)
DTS_B2H2: C802.1, D801.3 (K), R803.2, U801.2 (A)
DTS_B2L2: C821.1, D809.3 (K), R821.2, U804.2 (A)
DX_B2H2: D805.3 (COM), R815.2, R816.1, R818.1
DX_B2L2: D813.3 (COM), R833.2, R834.1, R836.1
DY_B2H2: D806.2 (A), R818.2
DY_B2L2: D814.2 (A), R836.2
FBVDD_B2H2: C812.1, R806.2, R807.1, U802.34 (FBVDD)
FBVDD_B2L2: C831.1, R824.2, R825.1, U805.34 (FBVDD)
FBVEE_B2H2: C813.1, R808.2, R809.1, U802.33 (FBVEE)
FBVEE_B2L2: C832.1, R826.2, R827.1, U805.33 (FBVEE)
GND: C801.2, C802.2, C803.2, C804.2, C805.2, C806.2, C807.2, C808.2, C809.2, C820.2, C821.2, C822.2, C823.2, C824.2, C825.2, C826.2, C827.2, C828.2, Q801.2 (S), Q802.2 (S), R801.2, R819.2, U801.3 (GND), U802.1 (GNDP), U802.2 (GNDP), U802.5 (GNDP), U802.8 (GNDP), U802.9 (GNDP), U802.10 (GNDP), U802.11 (GNDP), U802.12 (GNDP), U802.13 (GNDP), U802.14 (GNDP), U802.15 (GNDP), U802.16 (GNDP), U802.17 (GNDP), U802.18 (GNDP), U803.9 (GND), U804.3 (GND), U805.1 (GNDP), U805.2 (GNDP), U805.5 (GNDP), U805.8 (GNDP), U805.9 (GNDP), U805.10 (GNDP), U805.11 (GNDP), U805.12 (GNDP), U805.13 (GNDP), U805.14 (GNDP), U805.15 (GNDP), U805.16 (GNDP), U805.17 (GNDP), U805.18 (GNDP), U806.9 (GND)
G_B2H2: D803.3 (K), R812.2, R813.2, R814.1, U803.7 (CLMPI)
G_B2L2: D811.3 (K), R830.2, R831.2, R832.1, U806.7 (CLMPI)
INN_B2H2: C804.1, R804.2, U803.11 (IN-)
INN_B2L2: C823.1, R822.2, U806.11 (IN-)
INP_B2H2: C801.1, R802.2, U803.10 (IN+)
INP_B2L2: C820.1, R820.2, U806.10 (IN+)
KS_B2H2: C814.2, C815.2, C816.1, C817.1, C818.1, C819.2, D802.1 (A), D804.3 (K), D805.1 (A), R808.1, R810.2, R814.2, R817.2, U803.1 (AIN), U803.3 (COM)
KS_B2L2: C833.2, C834.2, C835.1, C836.1, C837.1, C838.2, D810.1 (A), D812.3 (K), D813.1 (A), R826.1, R828.2, R832.2, R835.2, U806.1 (AIN), U806.3 (COM)
OC_B2H2: C819.1, R816.2, R817.1, U803.2 (OC)
OC_B2L2: C838.1, R834.2, R835.1, U806.2 (OC)
OUTH_B2H2: R812.1, U803.4 (OUTH)
OUTH_B2L2: R830.1, U806.4 (OUTH)
OUTL_B2H2: R813.1, U803.6 (OUTL)
OUTL_B2L2: R831.1, U806.6 (OUTL)
P2_BUS+: D808.1 (K)
PG_B2H2: Q801.1 (G), R805.1, U802.3 (~PG)
PG_B2L2: Q802.1 (G), R823.1, U805.3 (~PG)
RLIMD_B2H2: D802.3 (K), R811.2
RLIMD_B2L2: D810.3 (K), R829.2
RLIM_B2H2: R810.1, R811.1, U802.32 (RLIM)
RLIM_B2L2: R828.1, R829.1, U805.32 (RLIM)
VDD_B2H2: C810.1, C811.1, C814.1, C815.1, D805.2 (K), R806.1, R815.1, U802.28 (VDD), U802.29 (VDD), U803.5 (VDD)
VDD_B2L2: C829.1, C830.1, C833.1, C834.1, D813.2 (K), R824.1, R833.1, U805.28 (VDD), U805.29 (VDD), U806.5 (VDD)
VEE_B2H2: C810.2, C811.2, C812.2, C813.2, C816.2, C817.2, C818.2, R807.2, R809.2, U802.19 (VEE), U802.20 (VEE), U802.21 (VEE), U802.22 (VEE), U802.23 (VEE), U802.24 (VEE), U802.25 (VEE), U802.26 (VEE), U802.27 (VEE), U802.30 (VEE), U802.31 (VEE), U802.35 (VEEA), U802.36 (VEE), U803.8 (VEE)
VEE_B2L2: C829.2, C830.2, C831.2, C832.2, C835.2, C836.2, C837.2, R825.2, R827.2, U805.19 (VEE), U805.20 (VEE), U805.21 (VEE), U805.22 (VEE), U805.23 (VEE), U805.24 (VEE), U805.25 (VEE), U805.26 (VEE), U805.27 (VEE), U805.30 (VEE), U805.31 (VEE), U805.35 (VEEA), U805.36 (VEE), U806.8 (VEE)
ZM_B2H2: D803.1 (A), D804.1 (A)
ZM_B2L2: D811.1 (A), D812.1 (A)

Notes on the sheet:
IN+ = own PWM; IN- = complementary switch, falling edge stretched 2.21k/100p (interlock + min dead time = max(firmware, hardware)). Bias PG (active low) pulls RDY low.
VDD-R1-DX; DX-R2-OC-R3/Cblk-COM; DX-Rs-3 x US1M-drain (SLUSD43B Fig 9-8). BAT54S keeps DX between COM and VDD against dv/dt through the string.
B2L2: ISOLATED BIAS +15 V / -4 V
CLMPI direct to the gate (active Miller clamp). Kelvin source = COM. Zener pair clamps the gate to about +17 V / -6.6 V when the driver cannot.
Die VGS of the OFF switch while its partner turns on: -0.55 V at 56.7 V/ns (dab_spec, I_M 2.0 A), +0.87 V at 80 V/ns (module max, 2.9 A) vs VGS(th) 1.44 V at 175 C: fine at the DAB rate, marginal at 80 V/ns (gdrv's own case, Roff 1 ohm: +1.19 V). Crss(800 V) understates the low-voltage Cgd: confirm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
B2L2: DESAT ON OC
B2H2: DRIVER AND GATE
MILLER MARGIN (GDRV REV 4 MODEL, ROFF 0.27 OHM, CLMPI DIRECT)
UCC14241-Q1, 24 V in, regulated +/-1.3 %, reinforced barrier. RDR: RLIM1 sources COM, RLIM2 + DLIM sink it.
B2H2: LOGIC SIDE
B2L2: DRIVER AND GATE
B2L2: LOGIC SIDE
B2H2: DESAT ON OC
B2H2: ISOLATED BIAS +15 V / -4 V
