vectivolt/PCM/hardware/DAB60/sheets/09_b2_if.kicad_sch

## KiCad design hardware/DAB60/sheets/09_b2_if.kicad_sch (2026-10-04)

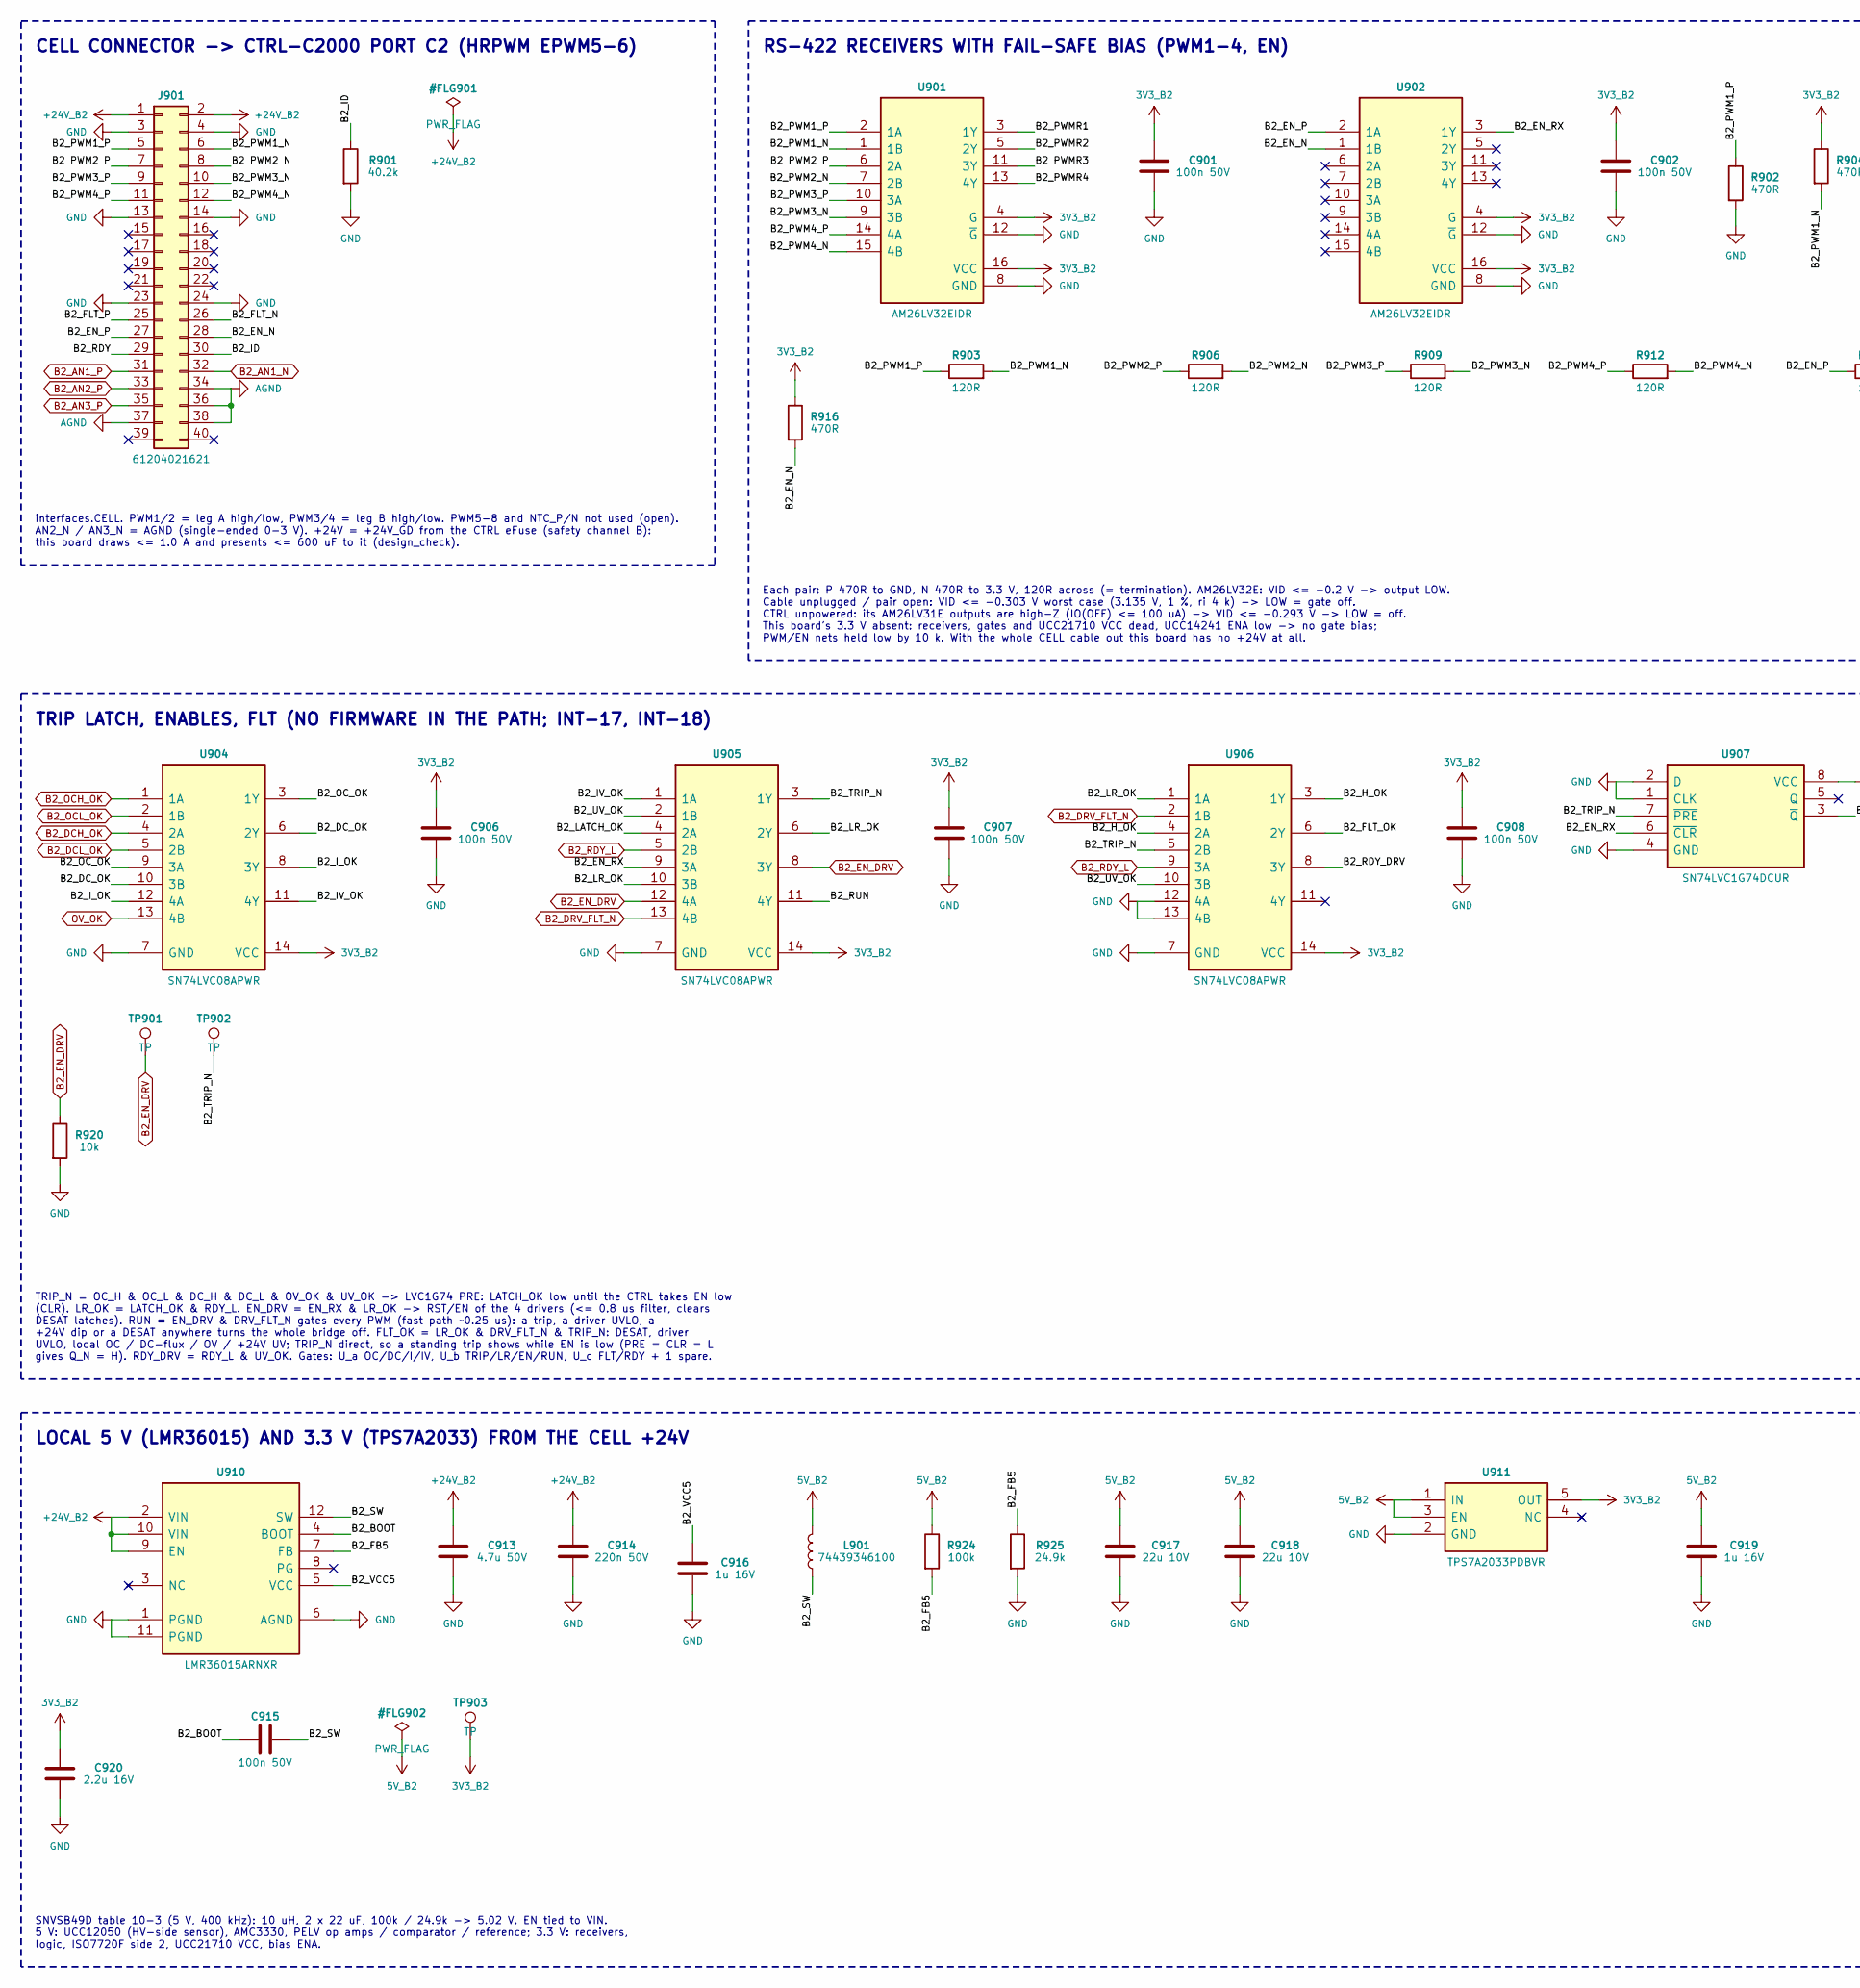
[picture p238: schematic 09_b2_if.kicad_sch, part in row 1, column 1]

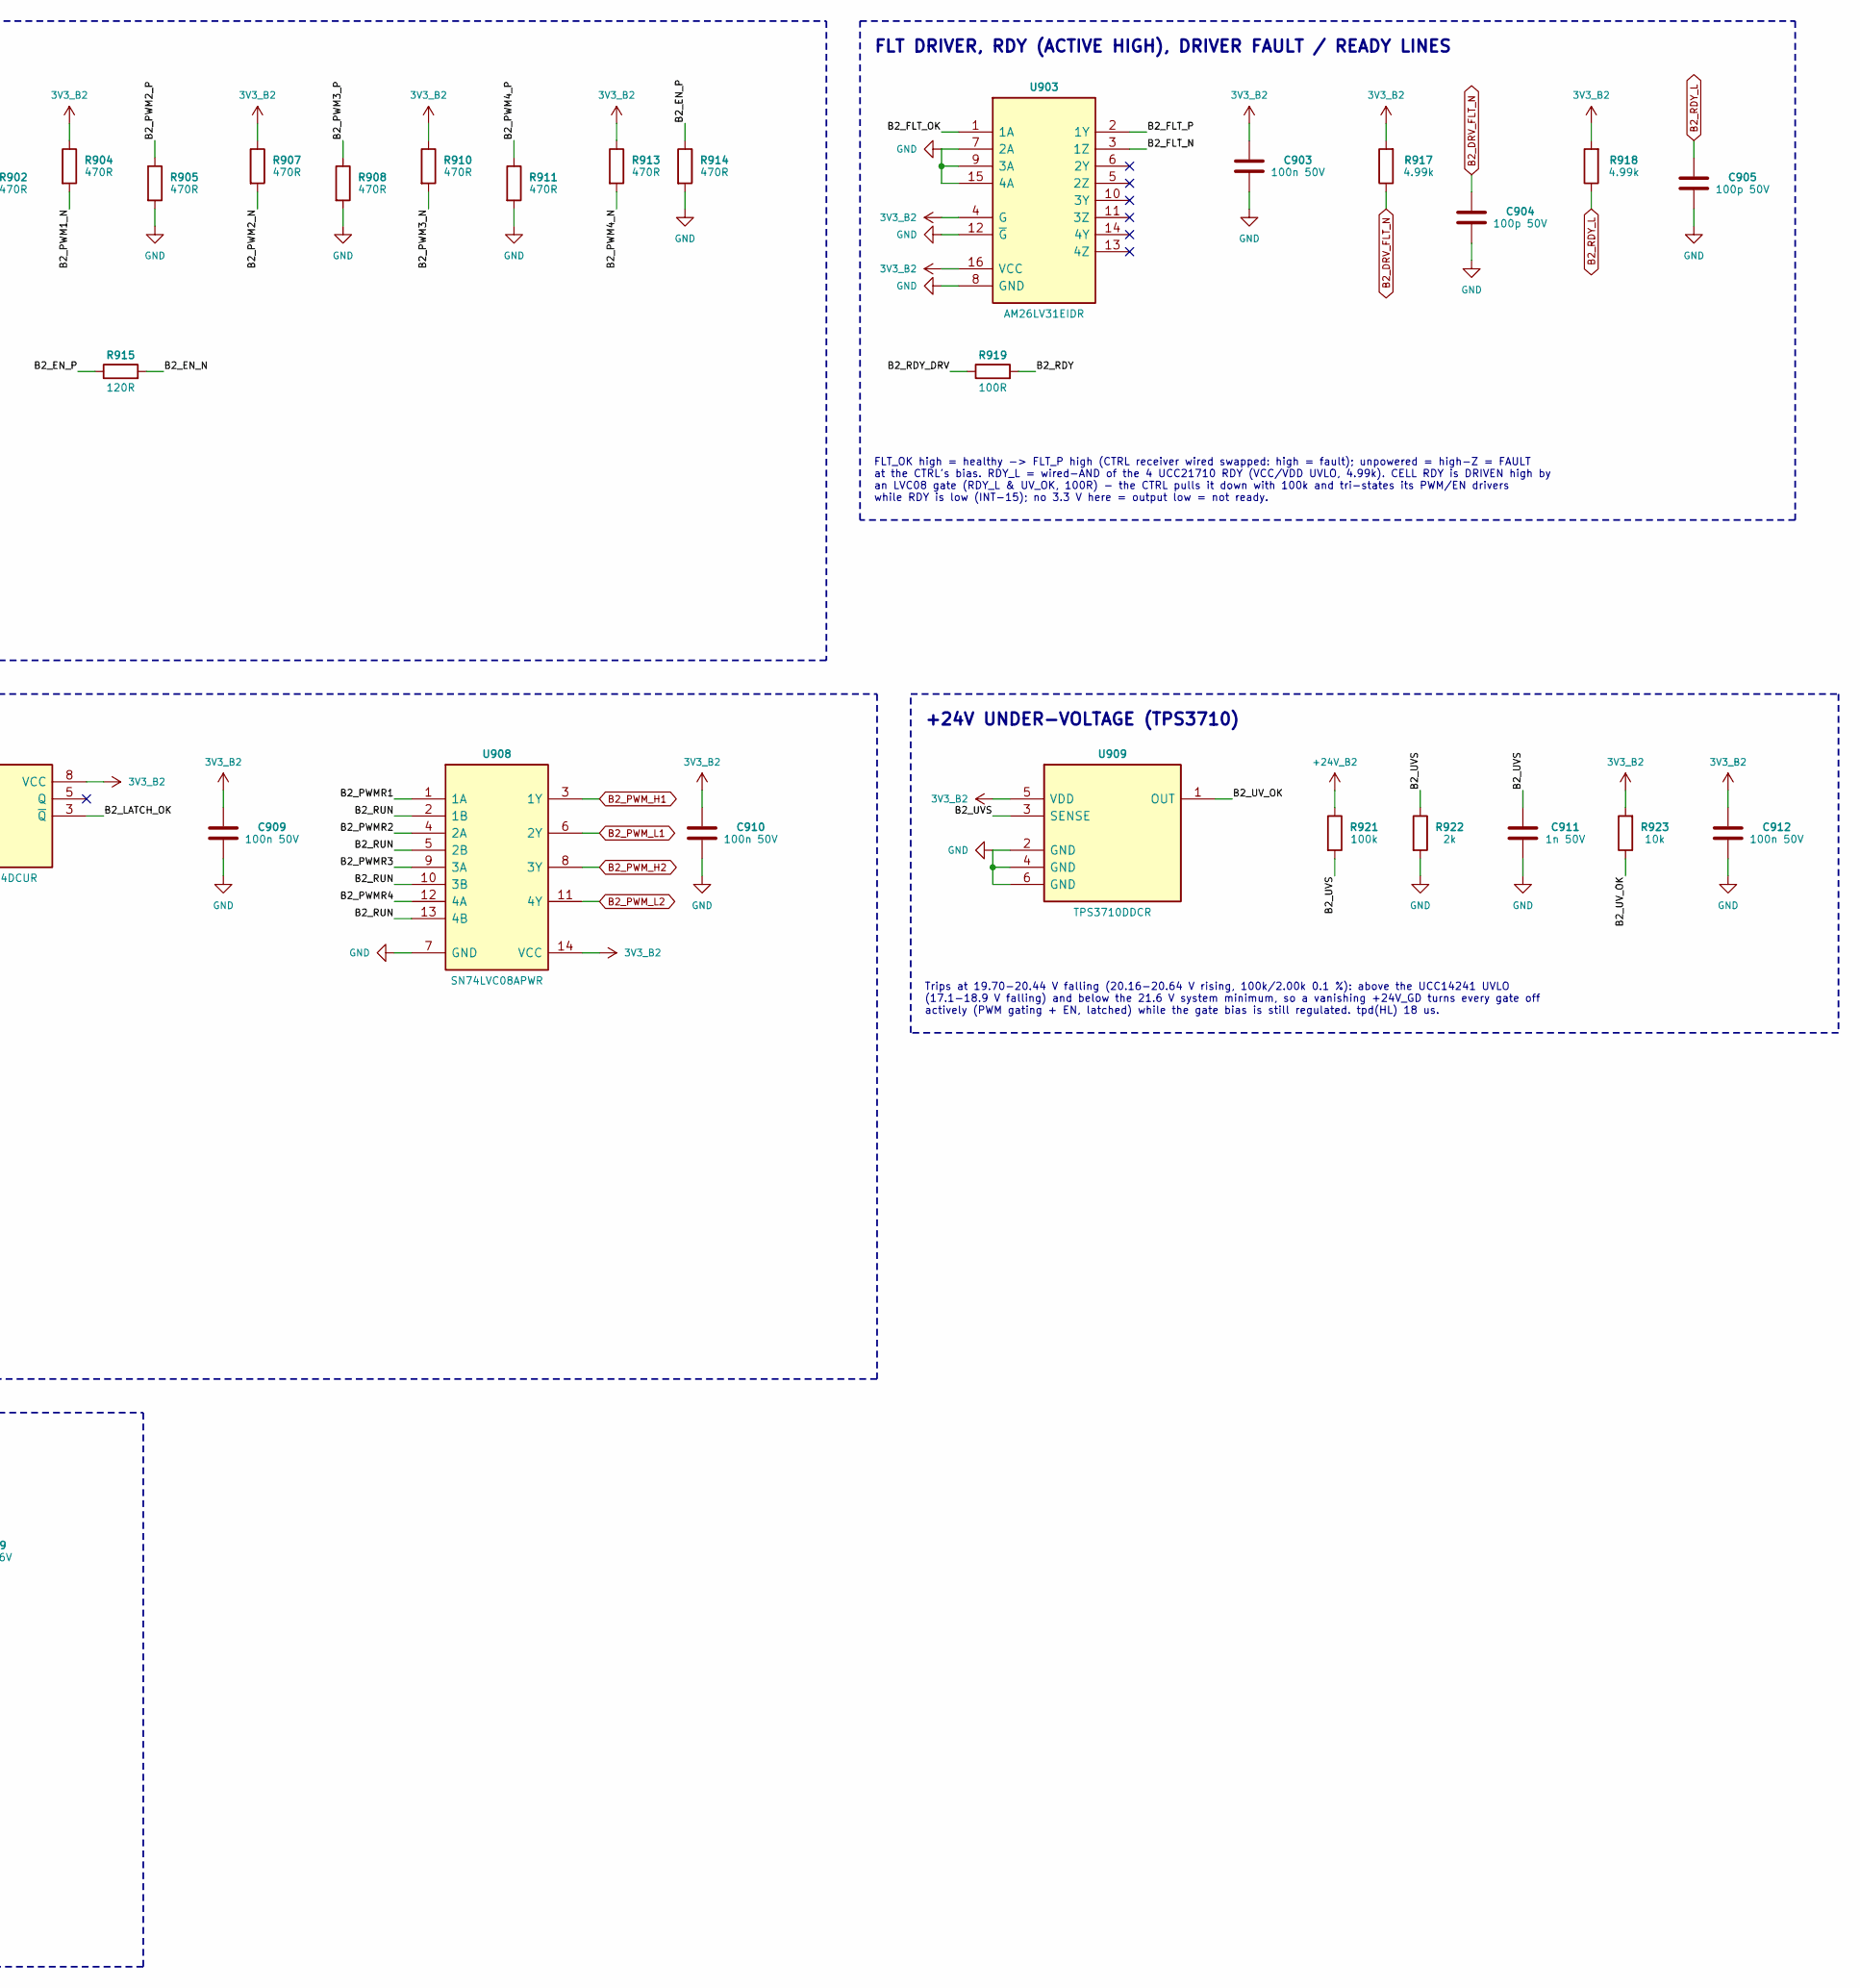
[picture p239: schematic 09_b2_if.kicad_sch, part in row 1, column 2]

Parts:
C901, C902, C903, C906, C907, C908, C909, C910, C912, C915: 100n 50V
C904, C905: 100p 50V
C911: 1n 50V
C913: 4.7u 50V
C914: 220n 50V
C916, C919: 1u 16V
C917, C918: 22u 10V
C920: 2.2u 16V
J901: 61204021621; MPN 61204021621
L901: 74439346100; MPN 74439346100
R901: 40.2k
R902, R904, R905, R907, R908, R910, R911, R913, R914, R916: 470R
R903, R906, R909, R912, R915: 120R
R917, R918: 4.99k
R919: 100R
R920, R923: 10k
R921, R924: 100k
R922: 2k
R925: 24.9k
TP901, TP902, TP903: TP
U901, U902: AM26LV32EIDR; MPN AM26LV32EIDR
U903: AM26LV31EIDR; MPN AM26LV31EIDR
U904, U905, U906, U908: SN74LVC08APWR; MPN SN74LVC08APWR
U907: SN74LVC1G74DCUR; MPN SN74LVC1G74DCUR
U909: TPS3710DDCR; MPN TPS3710DDCR
U910: LMR36015ARNXR; MPN LMR36015ARNXR
U911: TPS7A2033PDBVR; MPN TPS7A2033PDBVR

Connections:
3V3_B2: C901.1, C902.1, C903.1, C906.1, C907.1, C908.1, C909.1, C910.1, C912.1, C920.1, R904.1, R907.1, R910.1, R913.1, R916.1, R917.2, R918.2, R923.2, TP903.1, U901.4 (G), U901.16 (VCC), U902.4 (G), U902.16 (VCC), U903.4 (G), U903.16 (VCC), U904.14 (VCC), U905.14 (VCC), U906.14 (VCC), U907.8 (VCC), U908.14 (VCC), U909.5 (VDD), U911.5 (OUT)
5V_B2: C917.1, C918.1, C919.1, L901.2, R924.1, U911.1 (IN), U911.3 (EN)
+24V_B2: C913.1, C914.1, J901.1, J901.2, R921.1, U910.2 (VIN), U910.9 (EN), U910.10 (VIN)
AGND: J901.34, J901.36, J901.37, J901.38
B2_AN1_N: J901.32
B2_AN1_P: J901.31
B2_AN2_P: J901.33
B2_AN3_P: J901.35
B2_BOOT: C915.1, U910.4 (BOOT)
B2_DCH_OK: U904.4 (2A)
B2_DCL_OK: U904.5 (2B)
B2_DC_OK: U904.6 (2Y), U904.10 (3B)
B2_DRV_FLT_N: C904.1, R917.1, U905.13 (4B), U906.2 (1B)
B2_EN_DRV: R920.1, TP901.1, U905.8 (3Y), U905.12 (4A)
B2_EN_N: J901.28, R915.2, R916.2, U902.1 (1B)
B2_EN_P: J901.27, R914.1, R915.1, U902.2 (1A)
B2_EN_RX: U902.3 (1Y), U905.9 (3A), U907.6 (~CLR)
B2_FB5: R924.2, R925.1, U910.7 (FB)
B2_FLT_N: J901.26, U903.3 (1Z)
B2_FLT_OK: U903.1 (1A), U906.6 (2Y)
B2_FLT_P: J901.25, U903.2 (1Y)
B2_H_OK: U906.3 (1Y), U906.4 (2A)
B2_ID: J901.30, R901.1
B2_IV_OK: U904.11 (4Y), U905.1 (1A)
B2_I_OK: U904.8 (3Y), U904.12 (4A)
B2_LATCH_OK: U905.4 (2A), U907.3 (~Q)
B2_LR_OK: U905.6 (2Y), U905.10 (3B), U906.1 (1A)
B2_OCH_OK: U904.1 (1A)
B2_OCL_OK: U904.2 (1B)
B2_OC_OK: U904.3 (1Y), U904.9 (3A)
B2_PWM1_N: J901.6, R903.2, R904.2, U901.1 (1B)
B2_PWM1_P: J901.5, R902.1, R903.1, U901.2 (1A)
B2_PWM2_N: J901.8, R906.2, R907.2, U901.7 (2B)
B2_PWM2_P: J901.7, R905.1, R906.1, U901.6 (2A)
B2_PWM3_N: J901.10, R909.2, R910.2, U901.9 (3B)
B2_PWM3_P: J901.9, R908.1, R909.1, U901.10 (3A)
B2_PWM4_N: J901.12, R912.2, R913.2, U901.15 (4B)
B2_PWM4_P: J901.11, R911.1, R912.1, U901.14 (4A)
B2_PWMR1: U901.3 (1Y), U908.1 (1A)
B2_PWMR2: U901.5 (2Y), U908.4 (2A)
B2_PWMR3: U901.11 (3Y), U908.9 (3A)
B2_PWMR4: U901.13 (4Y), U908.12 (4A)
B2_PWM_H1: U908.3 (1Y)
B2_PWM_H2: U908.8 (3Y)
B2_PWM_L1: U908.6 (2Y)
B2_PWM_L2: U908.11 (4Y)
B2_RDY: J901.29, R919.2
B2_RDY_DRV: R919.1, U906.8 (3Y)
B2_RDY_L: C905.1, R918.1, U905.5 (2B), U906.9 (3A)
B2_RUN: U905.11 (4Y), U908.2 (1B), U908.5 (2B), U908.10 (3B), U908.13 (4B)
B2_SW: C915.2, L901.1, U910.12 (SW)
B2_TRIP_N: TP902.1, U905.3 (1Y), U906.5 (2B), U907.7 (~PRE)
B2_UVS: C911.1, R921.2, R922.1, U909.3 (SENSE)
B2_UV_OK: R923.1, U905.2 (1B), U906.10 (3B), U909.1 (OUT)
B2_VCC5: C916.1, U910.5 (VCC)
GND: C901.2, C902.2, C903.2, C904.2, C905.2, C906.2, C907.2, C908.2, C909.2, C910.2, C911.2, C912.2, C913.2, C914.2, C916.2, C917.2, C918.2, C919.2, C920.2, J901.3, J901.4, J901.13, J901.14, J901.23, J901.24, R901.2, R902.2, R905.2, R908.2, R911.2, R914.2, R920.2, R922.2, R925.2, U901.8 (GND), U901.12 (~G), U902.8 (GND), U902.12 (~G), U903.7 (2A), U903.8 (GND), U903.9 (3A), U903.12 (~G), U903.15 (4A), U904.7 (GND), U905.7 (GND), U906.7 (GND), U906.12 (4A), U906.13 (4B), U907.1 (CLK), U907.2 (D), U907.4 (GND), U908.7 (GND), U909.2 (GND), U909.4 (GND), U909.6 (GND), U910.1 (PGND), U910.6 (AGND), U910.11 (PGND), U911.2 (GND)
OV_OK: U904.13 (4B)

Notes on the sheet:
SNVSB49D table 10-3 (5 V, 400 kHz): 10 uH, 2 x 22 uF, 100k / 24.9k -> 5.02 V. EN tied to VIN. 5 V: UCC12050 (HV-side sensor), AMC3330, PELV op amps / comparator / reference; 3.3 V: receivers, logic, ISO7720F side 2, UCC21710 VCC, bias ENA.
Trips at 19.70-20.44 V falling (20.16-20.64 V rising, 100k/2.00k 0.1 %): above the UCC14241 UVLO (17.1-18.9 V falling) and below the 21.6 V system minimum, so a vanishing +24V_GD turns every gate off actively (PWM gating + EN, latched) while the gate bias is still regulated. tpd(HL) 18 us.
interfaces.CELL. PWM1/2 = leg A high/low, PWM3/4 = leg B high/low. PWM5-8 and NTC_P/N not used (open). AN2_N / AN3_N = AGND (single-ended 0-3 V). +24V = +24V_GD from the CTRL eFuse (safety channel B): this board draws <= 1.0 A and presents <= 600 uF to it (design_check).
FLT DRIVER, RDY (ACTIVE HIGH), DRIVER FAULT / READY LINES
Each pair: P 470R to GND, N 470R to 3.3 V, 120R across (= termination). AM26LV32E: VID <= -0.2 V -> output LOW. Cable unplugged / pair open: VID <= -0.303 V worst case (3.135 V, 1 %, ri 4 k) -> LOW = gate off. CTRL unpowered: its AM26LV31E outputs are high-Z (IO(OFF) <= 100 uA) -> VID <= -0.293 V -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
LOCAL 5 V (LMR36015) AND 3.3 V (TPS7A2033) FROM THE CELL +24V
TRIP_N = OC_H & OC_L & DC_H & DC_L & OV_OK & UV_OK -> LVC1G74 PRE: LATCH_OK low until the CTRL takes EN low (CLR). LR_OK = LATCH_OK & RDY_L. EN_DRV = EN_RX & LR_OK -> RST/EN of the 4 drivers (<= 0.8 us filter, clears DESAT latches). RUN = EN_DRV & DRV_FLT_N gates every PWM (fast path ~0.25 us): a t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
TRIP LATCH, ENABLES, FLT (NO FIRMWARE IN THE PATH; INT-17, INT-18)
RS-422 RECEIVERS WITH FAIL-SAFE BIAS (PWM1-4, EN)
CELL CONNECTOR -> CTRL-C2000 PORT C2 (HRPWM EPWM5-6)
FLT_OK high = healthy -> FLT_P high (CTRL receiver wired swapped: high = fault); unpowered = high-Z = FAULT at the CTRL's bias. RDY_L = wired-AND of the 4 UCC21710 RDY (VCC/VDD UVLO, 4.99k). CELL RDY is DRIVEN high by an LVC08 gate (RDY_L & UV_OK, 100R) - the CTRL pulls it down with 100k and tri-st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
+24V UNDER-VOLTAGE (TPS3710)
