vectivolt/PCM/hardware/DAB60/sheets/10_b2_sense.kicad_sch

## KiCad design hardware/DAB60/sheets/10_b2_sense.kicad_sch (2026-10-04)

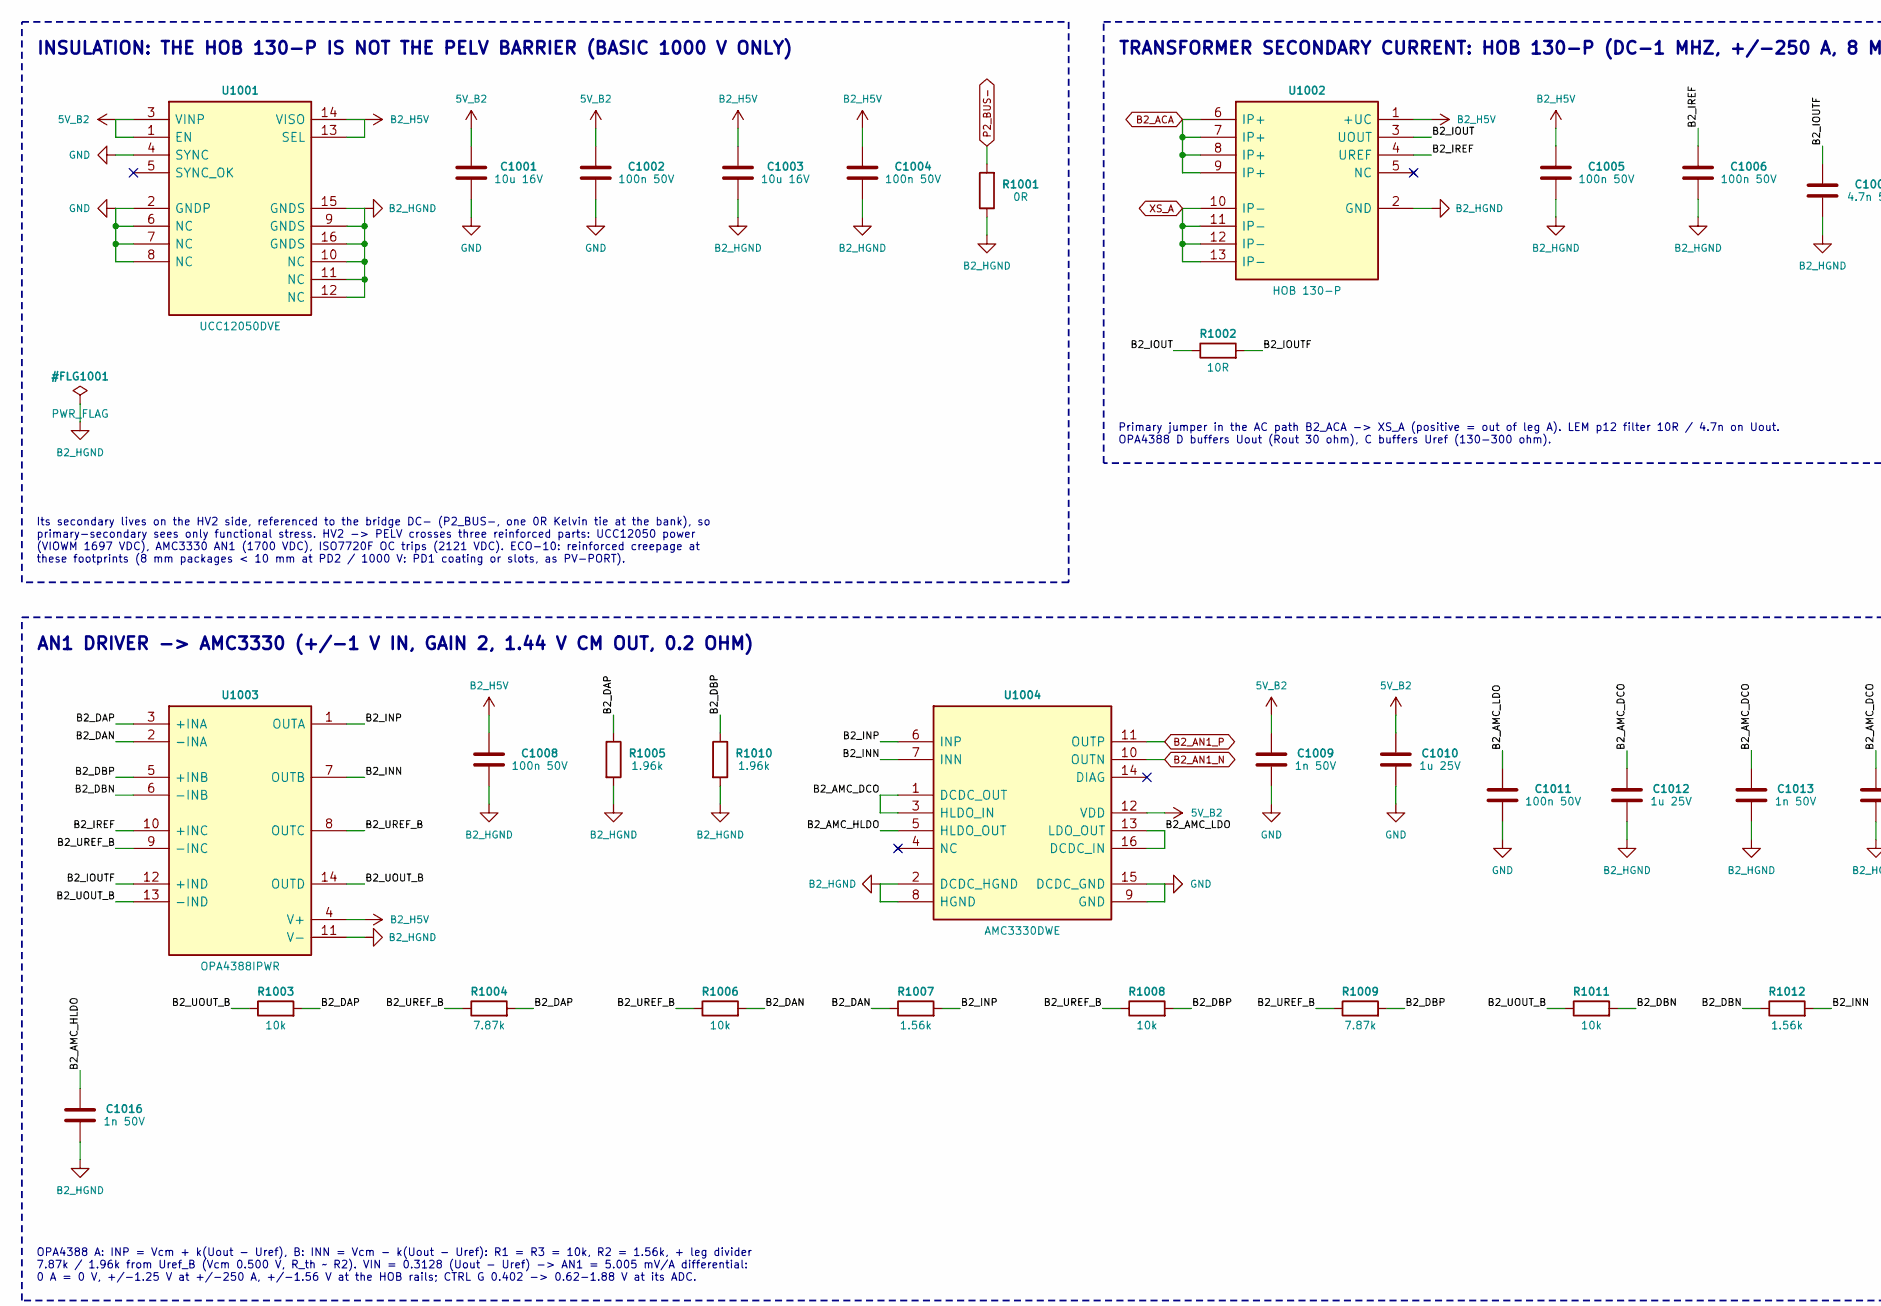
[picture p240: schematic 10_b2_sense.kicad_sch, part in row 1, column 1]

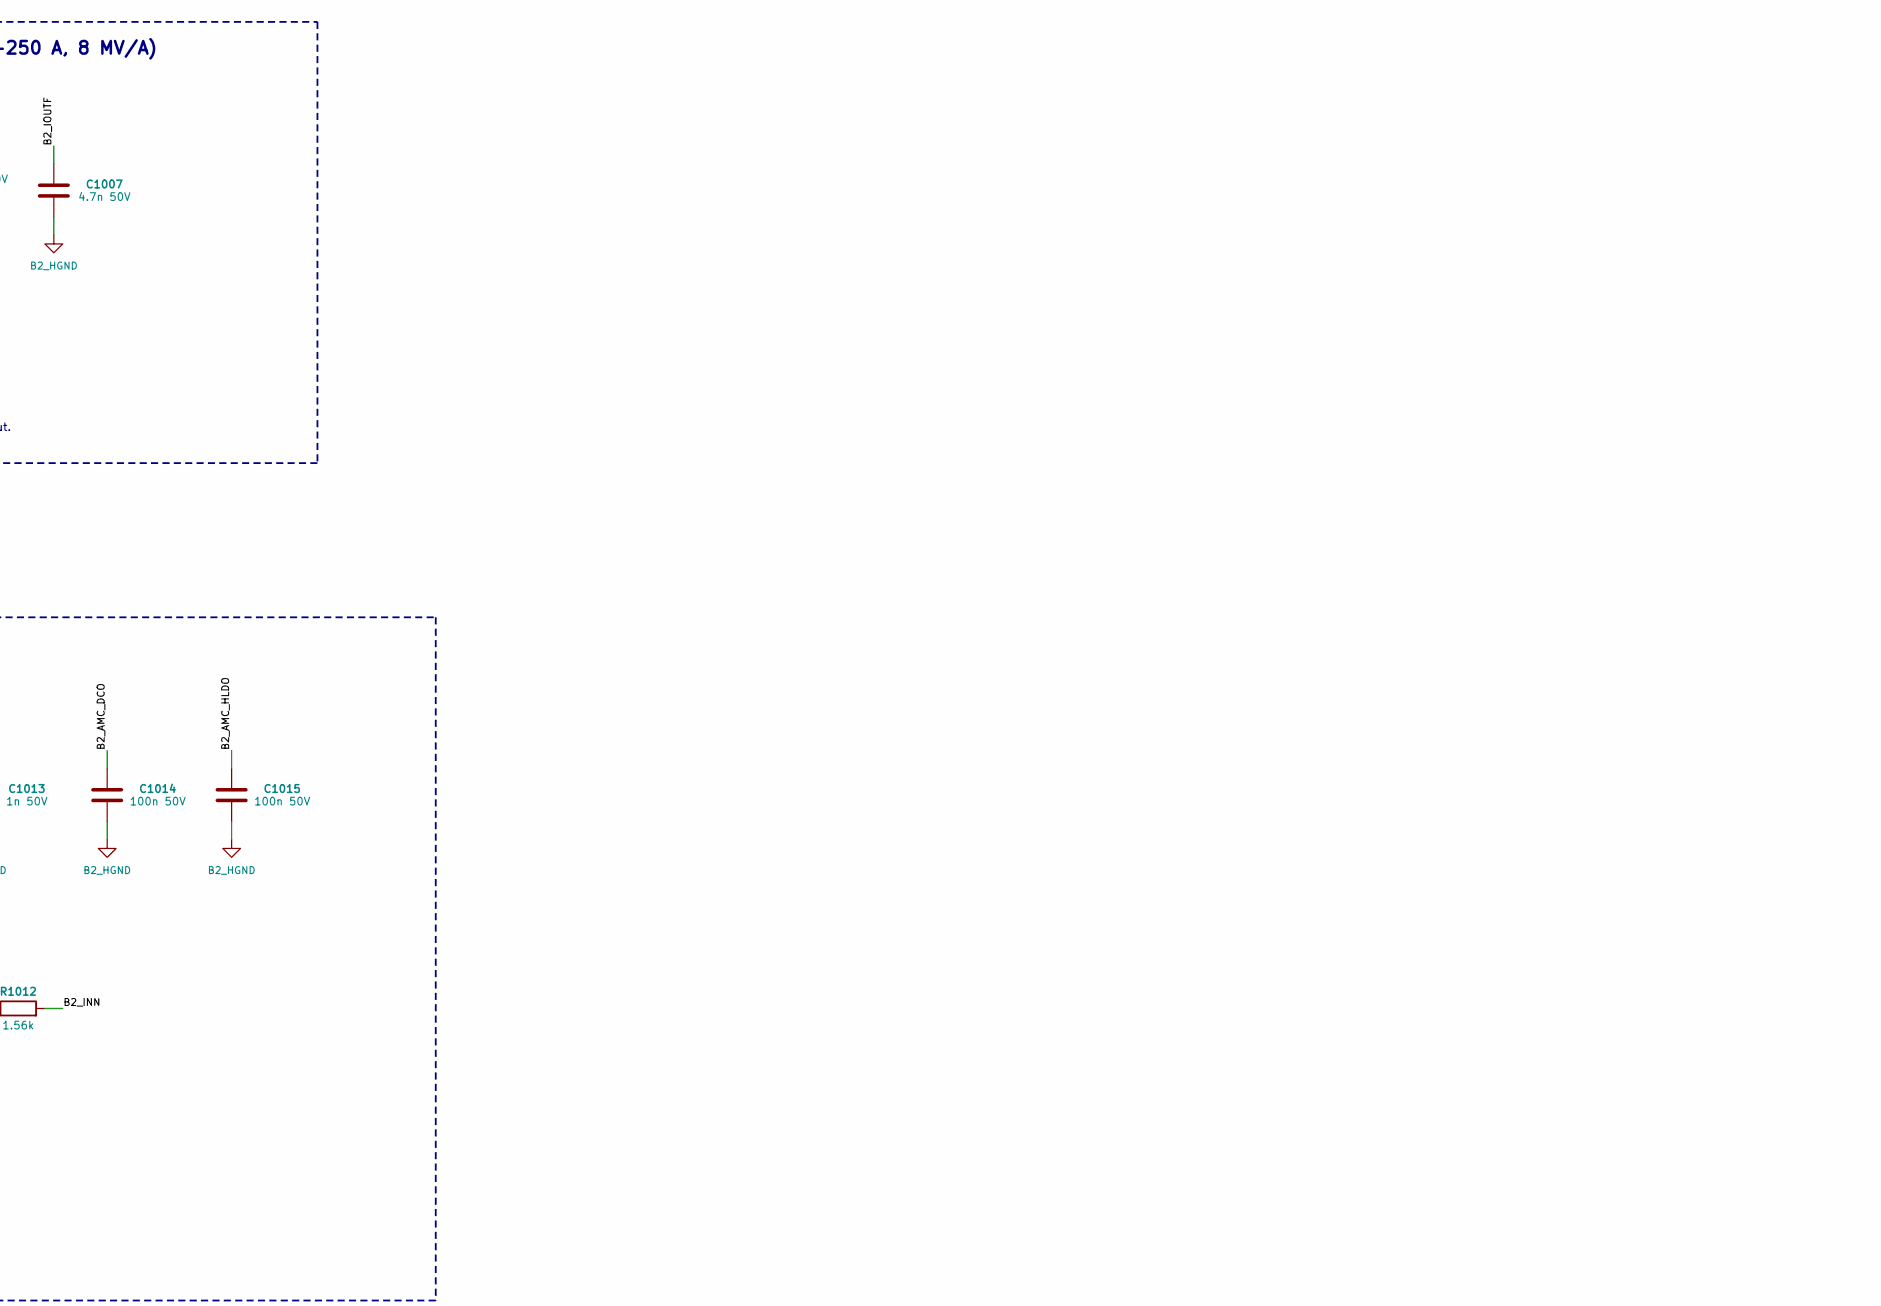
[picture p241: schematic 10_b2_sense.kicad_sch, part in row 1, column 2]

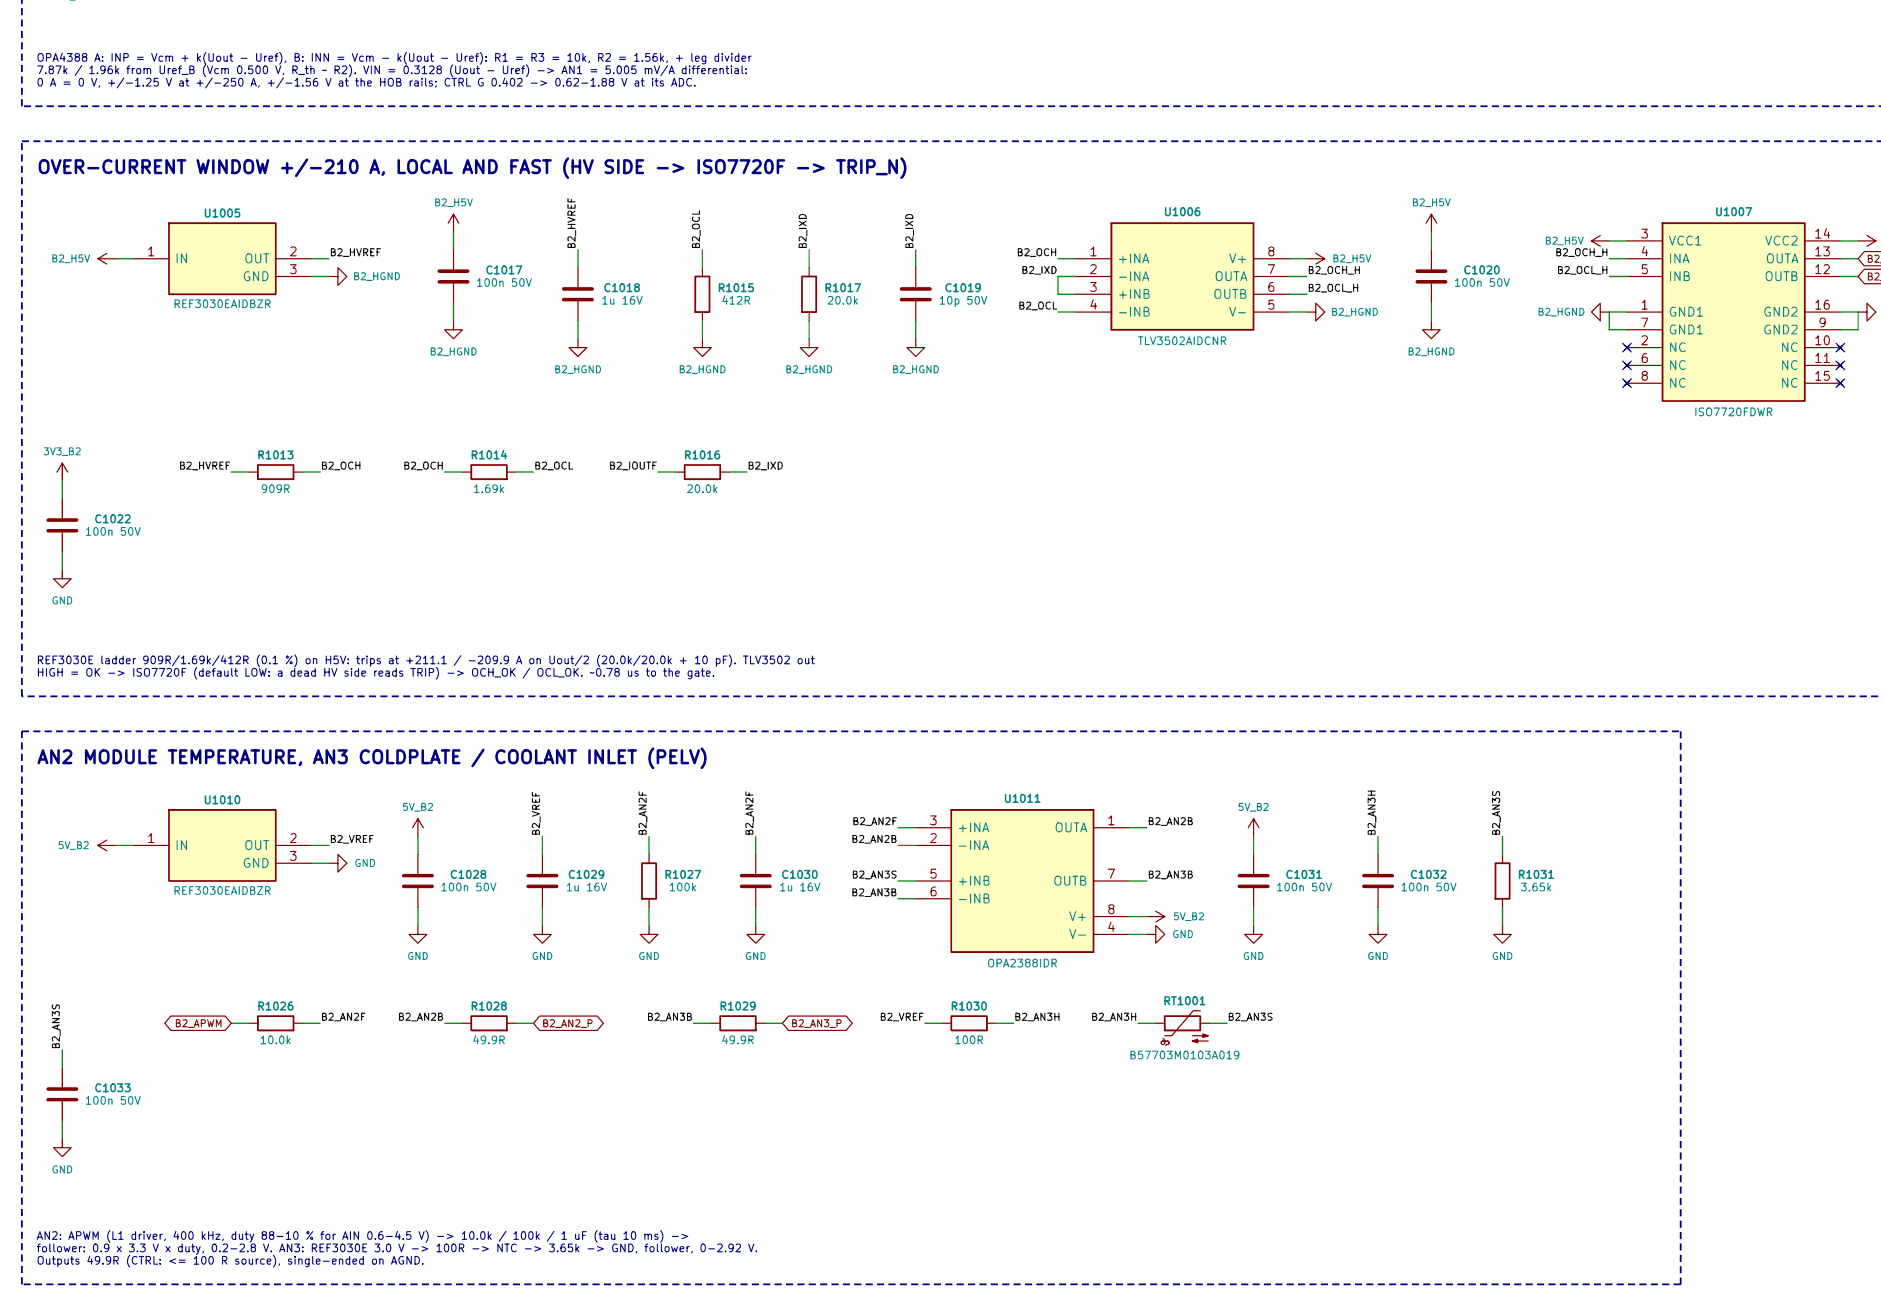
[picture p242: schematic 10_b2_sense.kicad_sch, part in row 2, column 1]

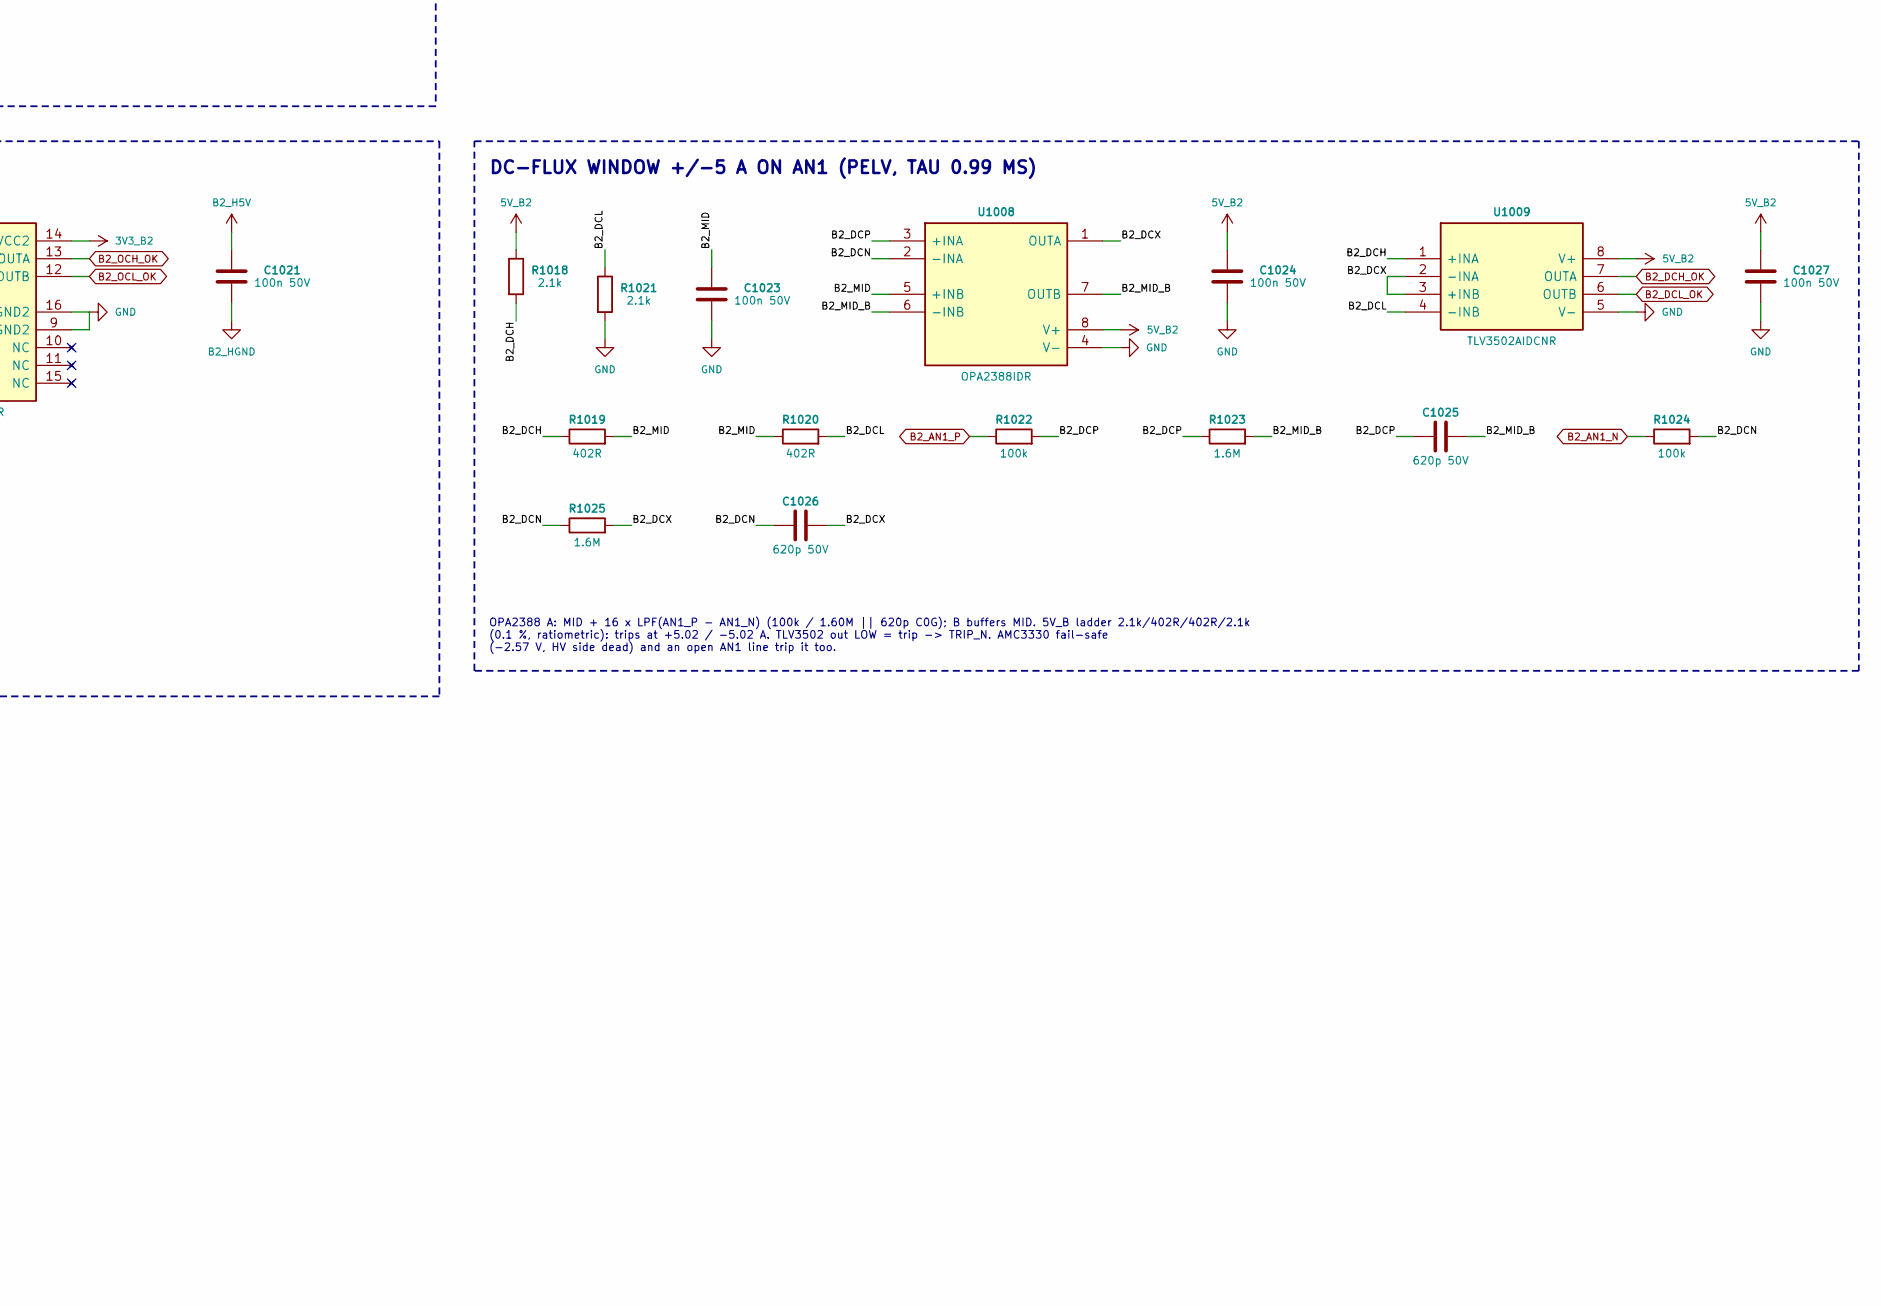
[picture p243: schematic 10_b2_sense.kicad_sch, part in row 2, column 2]

Parts:
C1001, C1003: 10u 16V
C1002, C1004, C1005, C1006, C1008, C1011, C1014, C1015, C1017, C1020, C1021, C1022, C1023, C1024, C1027, C1028, C1031, C1032, C1033: 100n 50V
C1007: 4.7n 50V
C1009, C1013, C1016: 1n 50V
C1010, C1012: 1u 25V
C1018, C1029, C1030: 1u 16V
C1019: 10p 50V
C1025, C1026: 620p 50V
R1001: 0R
R1002: 10R
R1003, R1006, R1008, R1011: 10k
R1004, R1009: 7.87k
R1005, R1010: 1.96k
R1007, R1012: 1.56k
R1013: 909R
R1014: 1.69k
R1015: 412R
R1016, R1017: 20.0k
R1018, R1021: 2.1k
R1019, R1020: 402R
R1022, R1024, R1027: 100k
R1023, R1025: 1.6M
R1026: 10.0k
R1028, R1029: 49.9R
R1030: 100R
R1031: 3.65k
RT1001: B57703M0103A019; MPN B57703M0103A019
U1001: UCC12050DVE; MPN UCC12050DVE
U1002: HOB 130-P; MPN HOB 130-P
U1003: OPA4388IPWR; MPN OPA4388IPWR
U1004: AMC3330DWE; MPN AMC3330DWE
U1005, U1010: REF3030EAIDBZR; MPN REF3030EAIDBZR
U1006, U1009: TLV3502AIDCNR; MPN TLV3502AIDCNR
U1007: ISO7720FDWR; MPN ISO7720FDWR
U1008, U1011: OPA2388IDR; MPN OPA2388IDR

Connections:
3V3_B2: C1022.1, U1007.14 (VCC2)
5V_B2: C1001.1, C1002.1, C1009.1, C1010.1, C1024.1, C1027.1, C1028.1, C1031.1, R1018.1, U1001.1 (EN), U1001.3 (VINP), U1004.12 (VDD), U1008.8 (V+), U1009.8 (V+), U1010.1 (IN), U1011.8 (V+)
B2_ACA: U1002.6 (IP+), U1002.7 (IP+), U1002.8 (IP+), U1002.9 (IP+)
B2_AMC_DCO: C1012.1, C1013.1, C1014.1, U1004.1 (DCDC_OUT), U1004.3 (HLDO_IN)
B2_AMC_HLDO: C1015.1, C1016.1, U1004.5 (HLDO_OUT)
B2_AMC_LDO: C1011.1, U1004.13 (LDO_OUT), U1004.16 (DCDC_IN)
B2_AN1_N: R1024.1, U1004.10 (OUTN)
B2_AN1_P: R1022.1, U1004.11 (OUTP)
B2_AN2B: R1028.1, U1011.1 (OUTA), U1011.2 (-INA)
B2_AN2F: C1030.1, R1026.2, R1027.1, U1011.3 (+INA)
B2_AN2_P: R1028.2
B2_AN3B: R1029.1, U1011.6 (-INB), U1011.7 (OUTB)
B2_AN3H: C1032.1, R1030.2, RT1001.1
B2_AN3S: C1033.1, R1031.1, RT1001.2, U1011.5 (+INB)
B2_AN3_P: R1029.2
B2_APWM: R1026.1
B2_DAN: R1006.2, R1007.1, U1003.2 (-INA)
B2_DAP: R1003.2, R1004.2, R1005.1, U1003.3 (+INA)
B2_DBN: R1011.2, R1012.1, U1003.6 (-INB)
B2_DBP: R1008.2, R1009.2, R1010.1, U1003.5 (+INB)
B2_DCH: R1018.2, R1019.1, U1009.1 (+INA)
B2_DCH_OK: U1009.7 (OUTA)
B2_DCL: R1020.2, R1021.1, U1009.4 (-INB)
B2_DCL_OK: U1009.6 (OUTB)
B2_DCN: C1026.1, R1024.2, R1025.1, U1008.2 (-INA)
B2_DCP: C1025.1, R1022.2, R1023.1, U1008.3 (+INA)
B2_DCX: C1026.2, R1025.2, U1008.1 (OUTA), U1009.2 (-INA), U1009.3 (+INB)
B2_H5V: C1003.1, C1004.1, C1005.1, C1008.1, C1017.1, C1020.1, C1021.1, U1001.13 (SEL), U1001.14 (VISO), U1002.1 (+UC), U1003.4 (V+), U1005.1 (IN), U1006.8 (V+), U1007.3 (VCC1)
B2_HGND: C1003.2, C1004.2, C1005.2, C1006.2, C1007.2, C1008.2, C1012.2, C1013.2, C1014.2, C1015.2, C1016.2, C1017.2, C1018.2, C1019.2, C1020.2, C1021.2, R1001.1, R1005.2, R1010.2, R1015.2, R1017.2, U1001.9 (GNDS), U1001.10 (NC), U1001.11 (NC), U1001.12 (NC), U1001.15 (GNDS), U1001.16 (GNDS), U1002.2 (GND), U1003.11 (V-), U1004.2 (DCDC_HGND), U1004.8 (HGND), U1005.3 (GND), U1006.5 (V-), U1007.1 (GND1), U1007.7 (GND1)
B2_HVREF: C1018.1, R1013.1, U1005.2 (OUT)
B2_INN: R1012.2, U1003.7 (OUTB), U1004.7 (INN)
B2_INP: R1007.2, U1003.1 (OUTA), U1004.6 (INP)
B2_IOUT: R1002.1, U1002.3 (UOUT)
B2_IOUTF: C1007.1, R1002.2, R1016.1, U1003.12 (+IND)
B2_IREF: C1006.1, U1002.4 (UREF), U1003.10 (+INC)
B2_IXD: C1019.1, R1016.2, R1017.1, U1006.2 (-INA), U1006.3 (+INB)
B2_MID: C1023.1, R1019.2, R1020.1, U1008.5 (+INB)
B2_MID_B: C1025.2, R1023.2, U1008.6 (-INB), U1008.7 (OUTB)
B2_OCH: R1013.2, R1014.1, U1006.1 (+INA)
B2_OCH_H: U1006.7 (OUTA), U1007.4 (INA)
B2_OCH_OK: U1007.13 (OUTA)
B2_OCL: R1014.2, R1015.1, U1006.4 (-INB)
B2_OCL_H: U1006.6 (OUTB), U1007.5 (INB)
B2_OCL_OK: U1007.12 (OUTB)
B2_UOUT_B: R1003.1, R1011.1, U1003.13 (-IND), U1003.14 (OUTD)
B2_UREF_B: R1004.1, R1006.1, R1008.1, R1009.1, U1003.8 (OUTC), U1003.9 (-INC)
B2_VREF: C1029.1, R1030.1, U1010.2 (OUT)
GND: C1001.2, C1002.2, C1009.2, C1010.2, C1011.2, C1022.2, C1023.2, C1024.2, C1027.2, C1028.2, C1029.2, C1030.2, C1031.2, C1032.2, C1033.2, R1021.2, R1027.2, R1031.2, U1001.2 (GNDP), U1001.4 (SYNC), U1001.6 (NC), U1001.7 (NC), U1001.8 (NC), U1004.9 (GND), U1004.15 (DCDC_GND), U1007.9 (GND2), U1007.16 (GND2), U1008.4 (V-), U1009.5 (V-), U1010.3 (GND), U1011.4 (V-)
P2_BUS-: R1001.2
XS_A: U1002.10 (IP-), U1002.11 (IP-), U1002.12 (IP-), U1002.13 (IP-)

Notes on the sheet:
OVER-CURRENT WINDOW +/-210 A, LOCAL AND FAST (HV SIDE -> ISO7720F -> TRIP_N)
OPA2388 A: MID + 16 x LPF(AN1_P - AN1_N) (100k / 1.60M || 620p C0G); B buffers MID. 5V_B ladder 2.1k/402R/402R/2.1k (0.1 %, ratiometric): trips at +5.02 / -5.02 A. TLV3502 out LOW = trip -> TRIP_N. AMC3330 fail-safe (-2.57 V, HV side dead) and an open AN1 line trip it too.
AN2: APWM (L1 driver, 400 kHz, duty 88-10 % for AIN 0.6-4.5 V) -> 10.0k / 100k / 1 uF (tau 10 ms) -> follower: 0.9 x 3.3 V x duty, 0.2-2.8 V. AN3: REF3030E 3.0 V -> 100R -> NTC -> 3.65k -> GND, follower, 0-2.92 V. Outputs 49.9R (CTRL: <= 100 R source), single-ended on AGND.
TRANSFORMER SECONDARY CURRENT: HOB 130-P (DC-1 MHZ, +/-250 A, 8 MV/A)
REF3030E ladder 909R/1.69k/412R (0.1 %) on H5V: trips at +211.1 / -209.9 A on Uout/2 (20.0k/20.0k + 10 pF). TLV3502 out HIGH = OK -> ISO7720F (default LOW: a dead HV side reads TRIP) -> OCH_OK / OCL_OK. ~0.78 us to the gate.
OPA4388 A: INP = Vcm + k(Uout - Uref), B: INN = Vcm - k(Uout - Uref): R1 = R3 = 10k, R2 = 1.56k, + leg divider 7.87k / 1.96k from Uref_B (Vcm 0.500 V, R_th ~ R2). VIN = 0.3128 (Uout - Uref) -> AN1 = 5.005 mV/A differential: 0 A = 0 V, +/-1.25 V at +/-250 A, +/-1.56 V at the HOB rails; CTRL G 0.402 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
AN2 MODULE TEMPERATURE, AN3 COLDPLATE / COOLANT INLET (PELV)
Its secondary lives on the HV2 side, referenced to the bridge DC- (P2_BUS-, one 0R Kelvin tie at the bank), so primary-secondary sees only functional stress. HV2 -> PELV crosses three reinforced parts: UCC12050 power (VIOWM 1697 VDC), AMC3330 AN1 (1700 VDC), ISO7720F OC trips (2121 VDC). ECO-10: re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
INSULATION: THE HOB 130-P IS NOT THE PELV BARRIER (BASIC 1000 V ONLY)
AN1 DRIVER -> AMC3330 (+/-1 V IN, GAIN 2, 1.44 V CM OUT, 0.2 OHM)
Primary jumper in the AC path B2_ACA -> XS_A (positive = out of leg A). LEM p12 filter 10R / 4.7n on Uout. OPA4388 D buffers Uout (Rout 30 ohm), C buffers Uref (130-300 ohm).
DC-FLUX WINDOW +/-5 A ON AN1 (PELV, TAU 0.99 MS)
