vectivolt/PCM/hardware/DAB60/sheets/11_magnetics.kicad_sch

## KiCad design hardware/DAB60/sheets/11_magnetics.kicad_sch (2026-10-04)

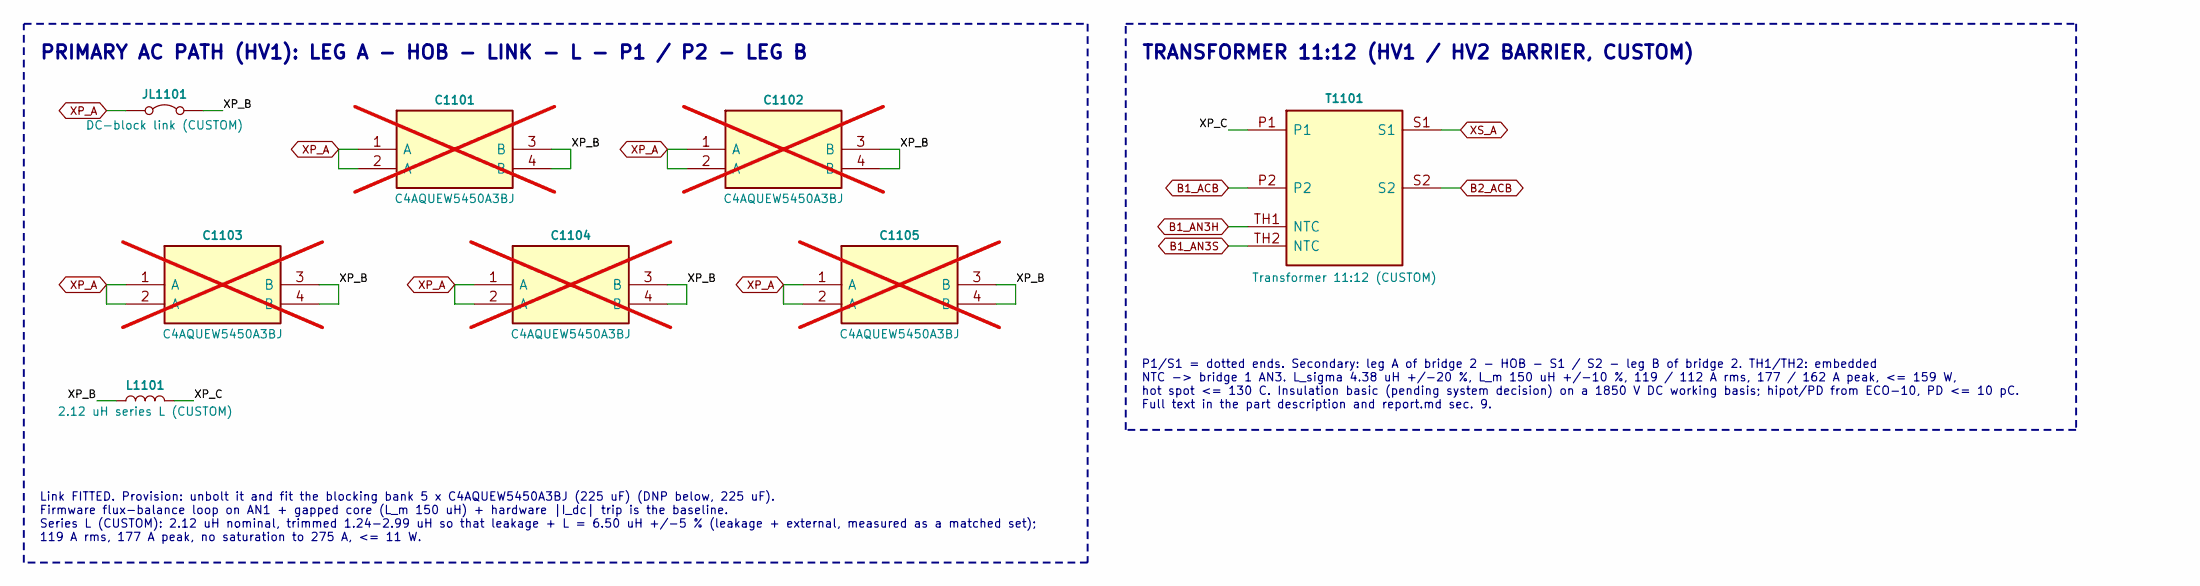
[picture p244: schematic 11_magnetics.kicad_sch]

Parts:
C1101, C1102, C1103, C1104, C1105: C4AQUEW5450A3BJ; MPN C4AQUEW5450A3BJ; not fitted
JL1101: DC-block link (CUSTOM)
L1101: 2.12 uH series L (CUSTOM)
T1101: Transformer 11:12 (CUSTOM)

Connections:
B1_ACB: T1101.P2
B1_AN3H: T1101.TH1 (NTC)
B1_AN3S: T1101.TH2 (NTC)
B2_ACB: T1101.S2
XP_A: C1101.1 (A), C1101.2 (A), C1102.1 (A), C1102.2 (A), C1103.1 (A), C1103.2 (A), C1104.1 (A), C1104.2 (A), C1105.1 (A), C1105.2 (A), JL1101.1 (A)
XP_B: C1101.3 (B), C1101.4 (B), C1102.3 (B), C1102.4 (B), C1103.3 (B), C1103.4 (B), C1104.3 (B), C1104.4 (B), C1105.3 (B), C1105.4 (B), JL1101.2 (B), L1101.1
XP_C: L1101.2, T1101.P1
XS_A: T1101.S1

Notes on the sheet:
PRIMARY AC PATH (HV1): LEG A - HOB - LINK - L - P1 / P2 - LEG B
P1/S1 = dotted ends. Secondary: leg A of bridge 2 - HOB - S1 / S2 - leg B of bridge 2. TH1/TH2: embedded NTC -> bridge 1 AN3. L_sigma 4.38 uH +/-20 %, L_m 150 uH +/-10 %, 119 / 112 A rms, 177 / 162 A peak, <= 159 W, hot spot <= 130 C. Insulation basic (pending system decision) on a 1850 V DC workin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
Link FITTED. Provision: unbolt it and fit the blocking bank 5 x C4AQUEW5450A3BJ (225 uF) (DNP below, 225 uF). Firmware flux-balance loop on AN1 + gapped core (L_m 150 uH) + hardware |I_dc| trip is the baseline. Series L (CUSTOM): 2.12 uH nominal, trimmed 1.24-2.99 uH so that leakage + L = 6.50 uH +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
TRANSFORMER 11:12 (HV1 / HV2 BARRIER, CUSTOM)
