vectivolt/PCM/hardware/DAB60/sheets/12_portA_power.kicad_sch

## KiCad design hardware/DAB60/sheets/12_portA_power.kicad_sch (2026-10-04)

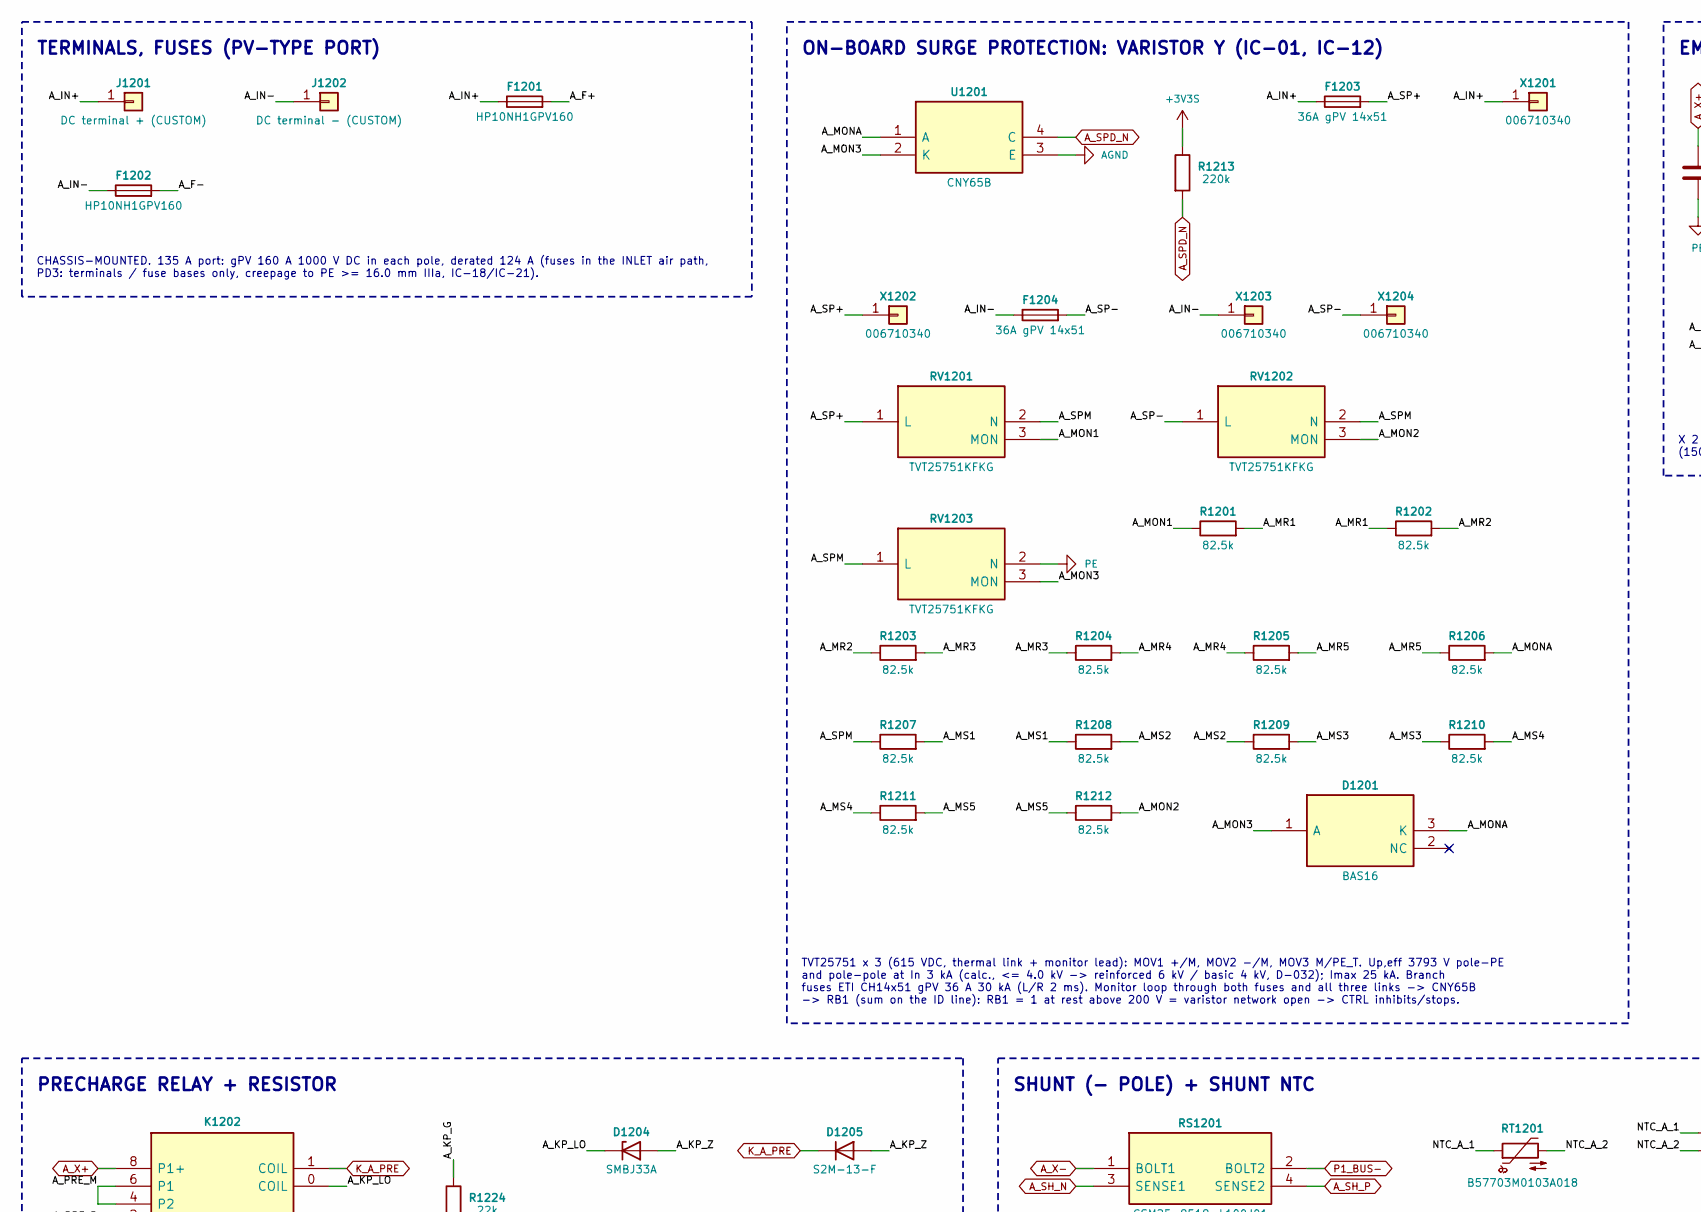
[picture p245: schematic 12_portA_power.kicad_sch, part in row 1, column 1]

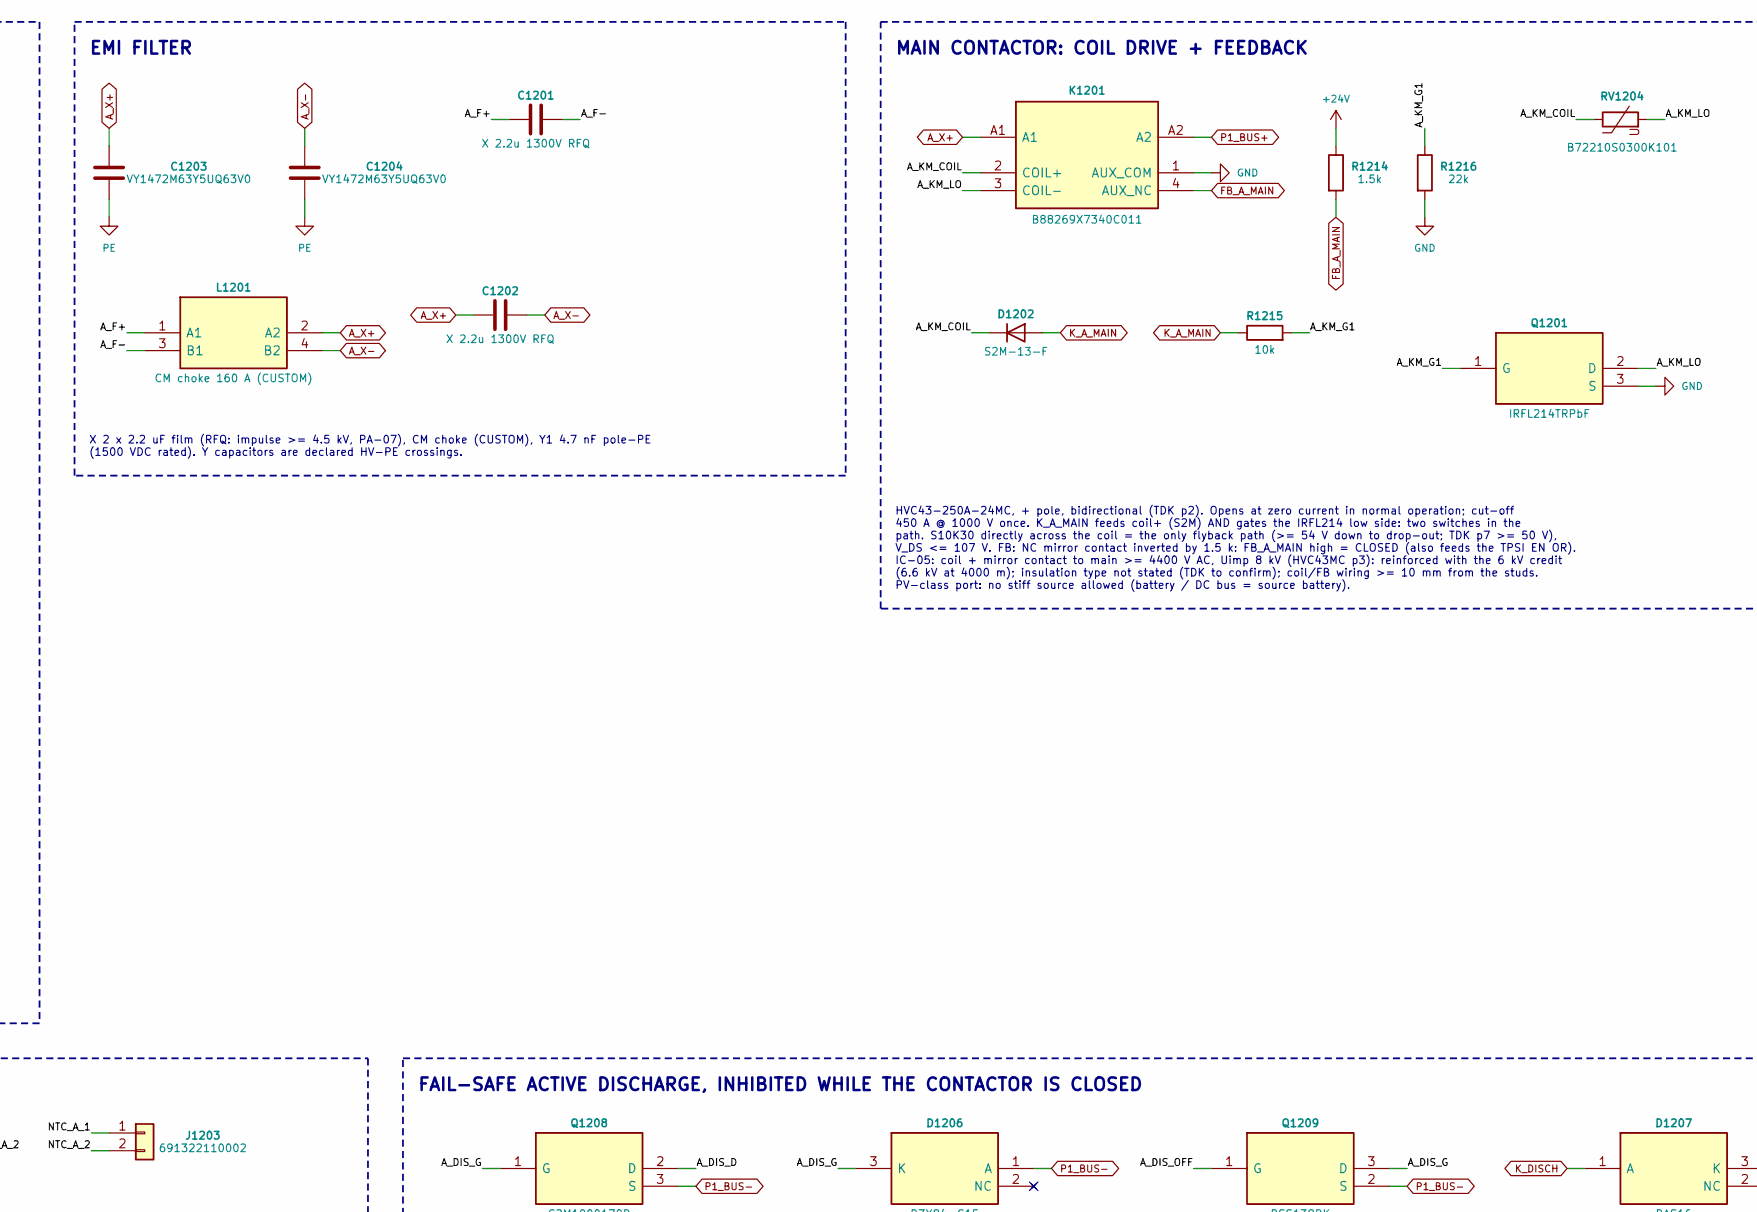
[picture p246: schematic 12_portA_power.kicad_sch, part in row 1, column 2]

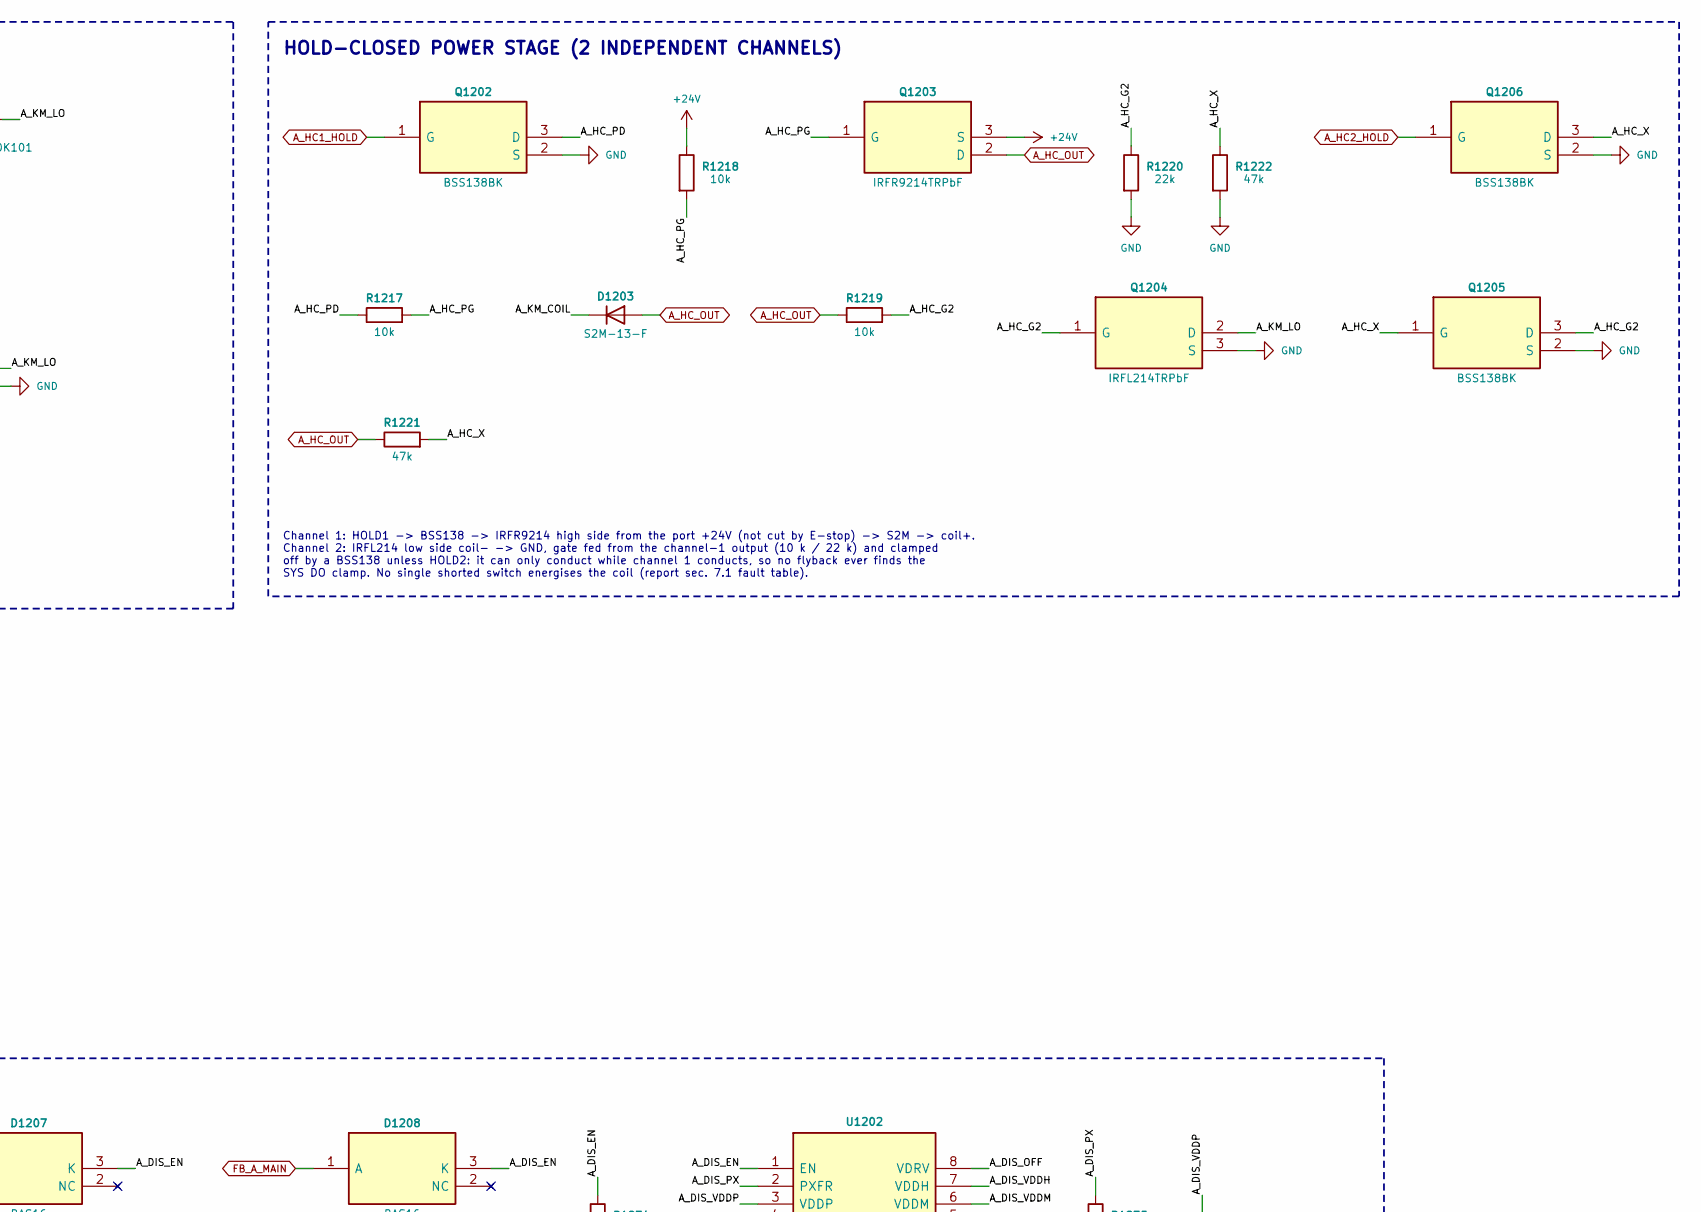
[picture p247: schematic 12_portA_power.kicad_sch, part in row 1, column 3]

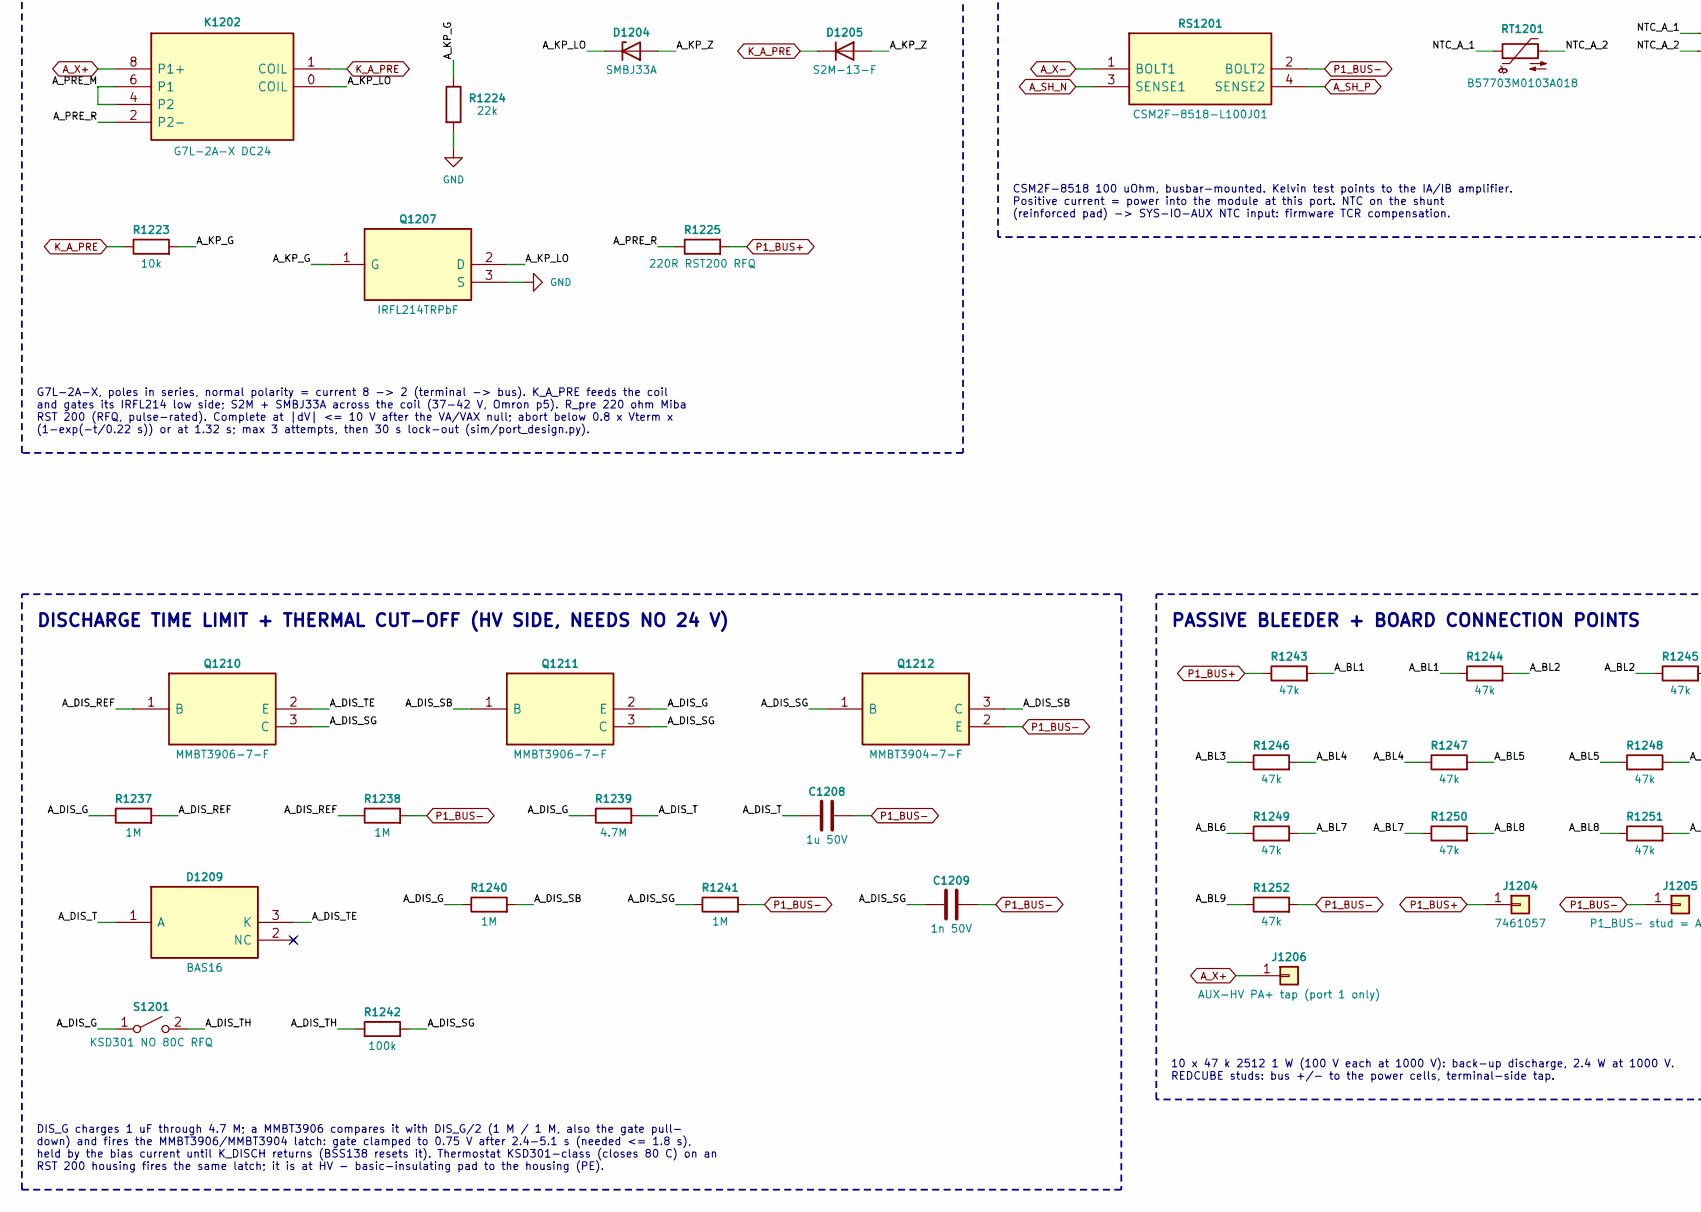
[picture p248: schematic 12_portA_power.kicad_sch, part in row 2, column 1]

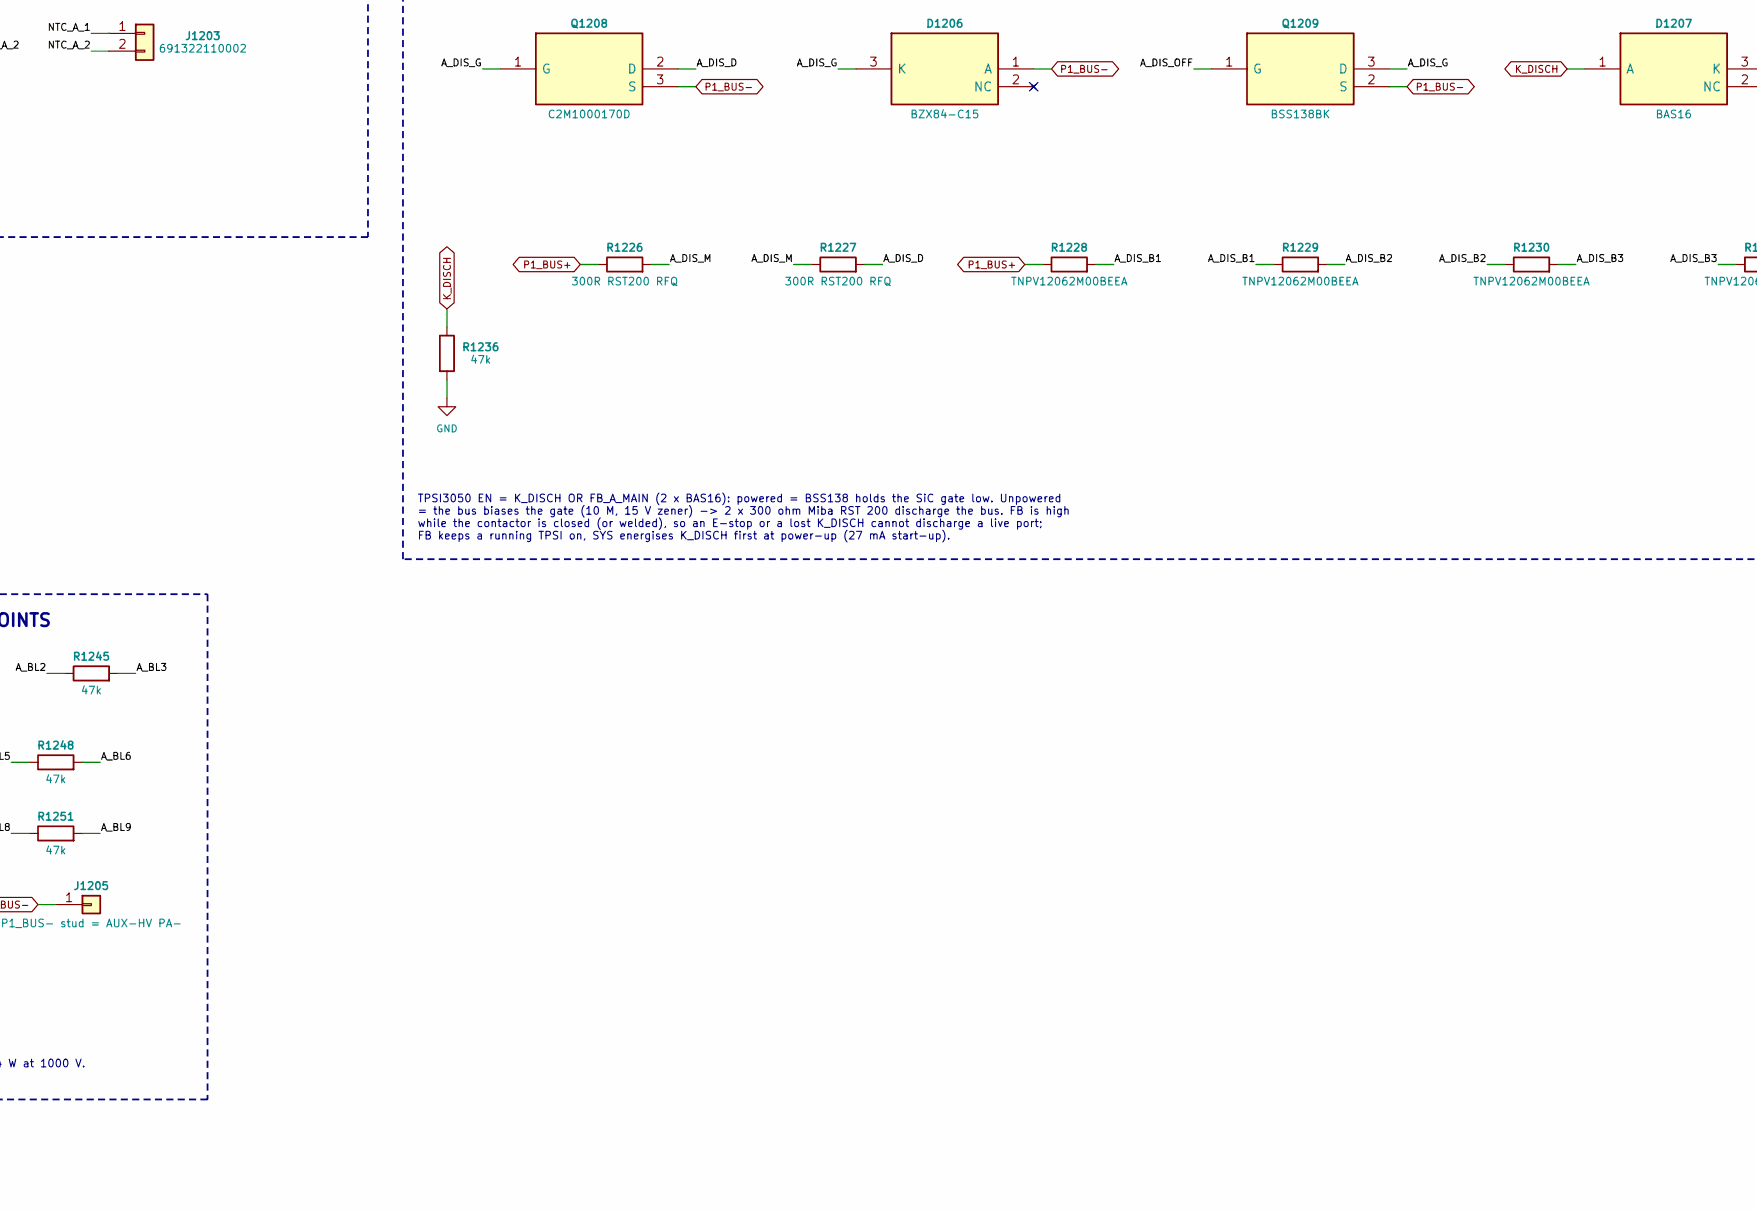
[picture p249: schematic 12_portA_power.kicad_sch, part in row 2, column 2]

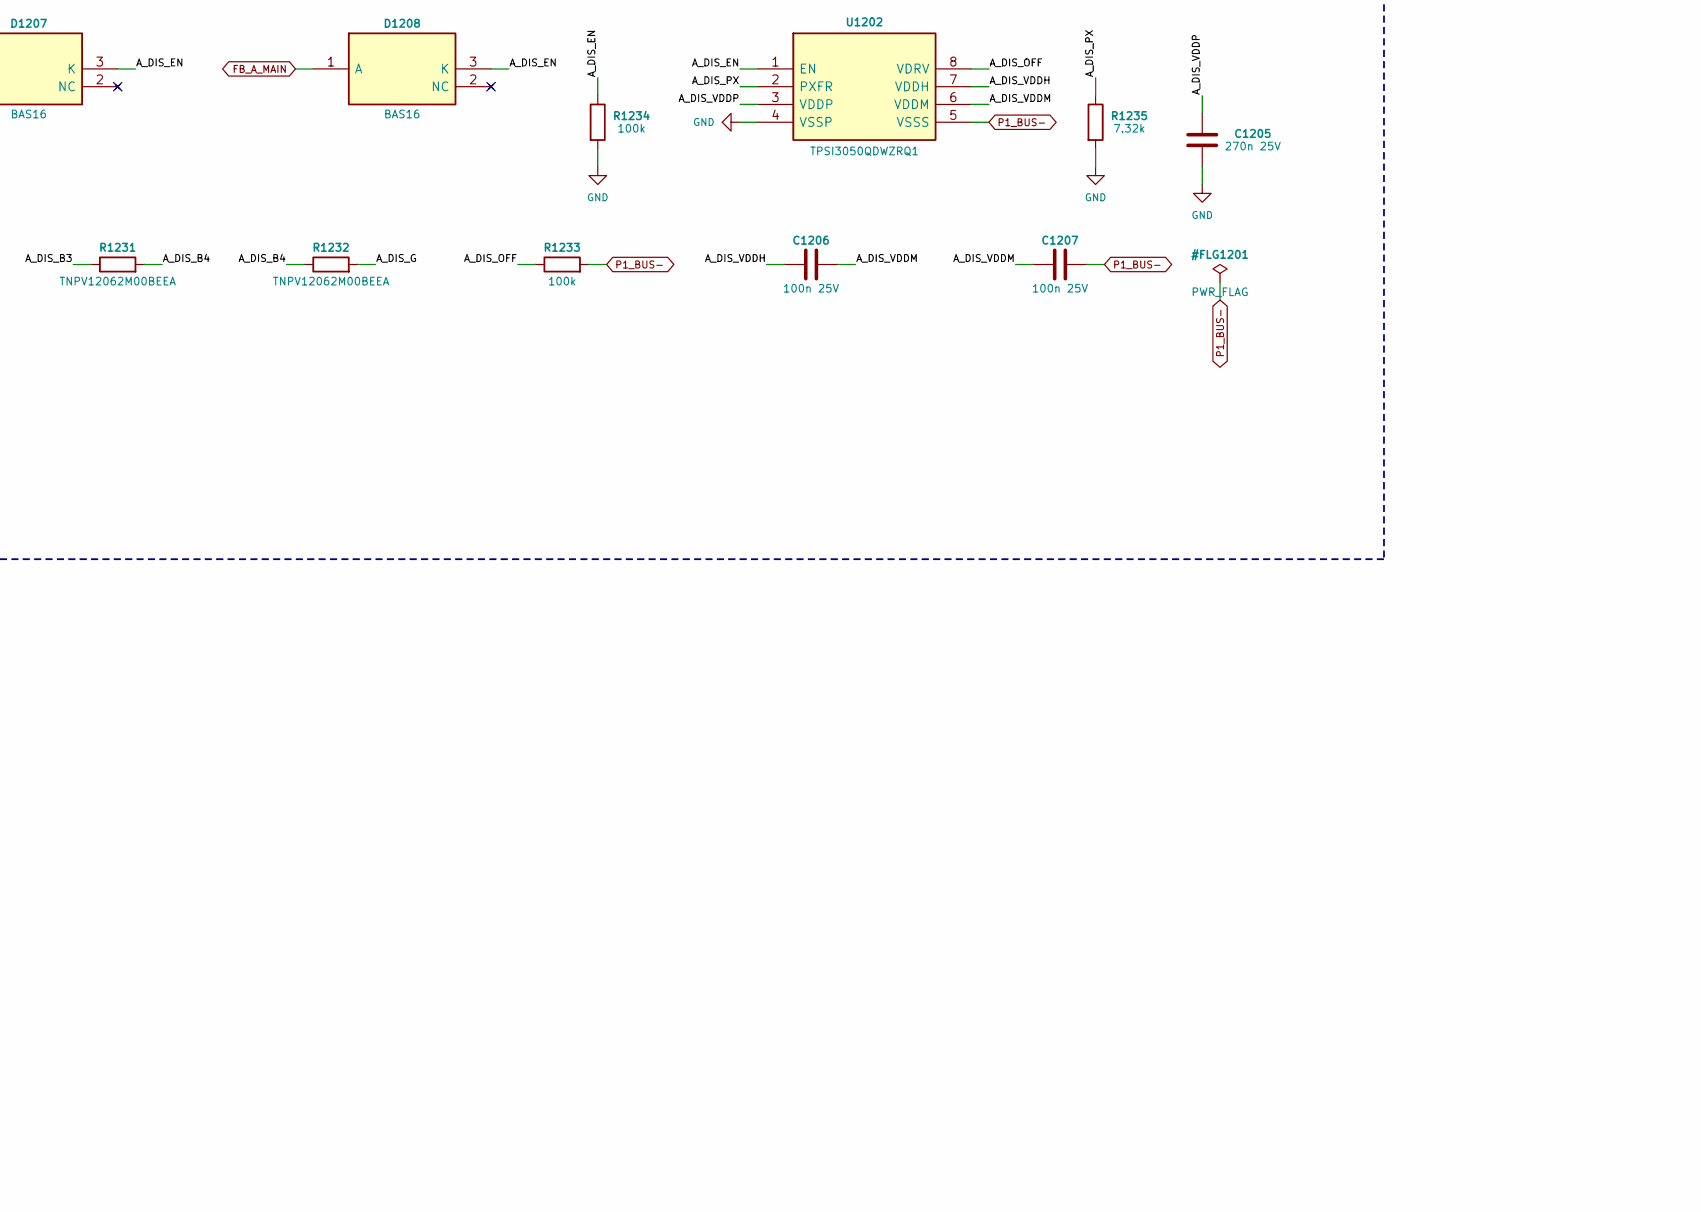
[picture p250: schematic 12_portA_power.kicad_sch, part in row 2, column 3]

Parts:
C1201, C1202: X 2.2u 1300V RFQ
C1203, C1204: VY1472M63Y5UQ63V0; MPN VY1472M63Y5UQ63V0
C1205: 270n 25V
C1206, C1207: 100n 25V
C1208: 1u 50V
C1209: 1n 50V
D1201, D1207, D1208, D1209: BAS16; MPN BAS16
D1202, D1203, D1205: S2M-13-F; MPN S2M-13-F
D1204: SMBJ33A; MPN SMBJ33A
D1206: BZX84-C15; MPN BZX84-C15
F1201, F1202: HP10NH1GPV160; MPN HP10NH1GPV160
F1203, F1204: 36A gPV 14x51; MPN 002637115
J1201: DC terminal + (CUSTOM)
J1202: DC terminal - (CUSTOM)
J1203: 691322110002; MPN 691322110002
J1204: 7461057; MPN 7461057
J1205: P1_BUS- stud = AUX-HV PA-; MPN 7461057
J1206: AUX-HV PA+ tap (port 1 only); MPN 7461057
K1201: B88269X7340C011; MPN B88269X7340C011
K1202: G7L-2A-X DC24; MPN G7L-2A-X DC24
L1201: CM choke 160 A (CUSTOM)
Q1201, Q1204, Q1207: IRFL214TRPbF; MPN IRFL214TRPbF
Q1202, Q1205, Q1206, Q1209: BSS138BK; MPN BSS138BK
Q1203: IRFR9214TRPbF; MPN IRFR9214TRPbF
Q1208: C2M1000170D; MPN C2M1000170D
Q1210, Q1211: MMBT3906-7-F; MPN MMBT3906-7-F
Q1212: MMBT3904-7-F; MPN MMBT3904-7-F
R1201, R1202, R1203, R1204, R1205, R1206, R1207, R1208, R1209, R1210, R1211, R1212: 82.5k
R1213: 220k
R1214: 1.5k
R1215, R1217, R1218, R1219, R1223: 10k
R1216, R1220, R1224: 22k
R1221, R1222, R1236, R1243, R1244, R1245, R1246, R1247, R1248, R1249, R1250, R1251, R1252: 47k
R1225: 220R RST200 RFQ
R1226, R1227: 300R RST200 RFQ
R1228, R1229, R1230, R1231, R1232: TNPV12062M00BEEA; MPN TNPV12062M00BEEA
R1233, R1234, R1242: 100k
R1235: 7.32k
R1237, R1238, R1240, R1241: 1M
R1239: 4.7M
RS1201: CSM2F-8518-L100J01; MPN CSM2F-8518-L100J01
RT1201: B57703M0103A018; MPN B57703M0103A018
RV1201, RV1202, RV1203: TVT25751KFKG; MPN TVT25751KFKG
RV1204: B72210S0300K101; MPN B72210S0300K101
S1201: KSD301 NO 80C RFQ
U1201: CNY65B; MPN CNY65B
U1202: TPSI3050QDWZRQ1; MPN TPSI3050QDWZRQ1
X1201, X1202, X1203, X1204: 006710340; MPN 006710340

Connections:
+3V3S: R1213.1
+24V: Q1203.3 (S), R1214.1, R1218.1
AGND: U1201.3 (E)
A_BL1: R1243.2, R1244.1
A_BL2: R1244.2, R1245.1
A_BL3: R1245.2, R1246.1
A_BL4: R1246.2, R1247.1
A_BL5: R1247.2, R1248.1
A_BL6: R1248.2, R1249.1
A_BL7: R1249.2, R1250.1
A_BL8: R1250.2, R1251.1
A_BL9: R1251.2, R1252.1
A_DIS_B1: R1228.2, R1229.1
A_DIS_B2: R1229.2, R1230.1
A_DIS_B3: R1230.2, R1231.1
A_DIS_B4: R1231.2, R1232.1
A_DIS_D: Q1208.2 (D), R1227.2
A_DIS_EN: D1207.3 (K), D1208.3 (K), R1234.1, U1202.1 (EN)
A_DIS_G: D1206.3 (K), Q1208.1 (G), Q1209.3 (D), Q1211.2 (E), R1232.2, R1237.1, R1239.1, R1240.1, S1201.1 (A)
A_DIS_M: R1226.2, R1227.1
A_DIS_OFF: Q1209.1 (G), R1233.1, U1202.8 (VDRV)
A_DIS_PX: R1235.1, U1202.2 (PXFR)
A_DIS_REF: Q1210.1 (B), R1237.2, R1238.1
A_DIS_SB: Q1211.1 (B), Q1212.3 (C), R1240.2
A_DIS_SG: C1209.1, Q1210.3 (C), Q1211.3 (C), Q1212.1 (B), R1241.1, R1242.2
A_DIS_T: C1208.1, D1209.1 (A), R1239.2
A_DIS_TE: D1209.3 (K), Q1210.2 (E)
A_DIS_TH: R1242.1, S1201.2 (B)
A_DIS_VDDH: C1206.1, U1202.7 (VDDH)
A_DIS_VDDM: C1206.2, C1207.1, U1202.6 (VDDM)
A_DIS_VDDP: C1205.1, U1202.3 (VDDP)
A_F+: C1201.1, F1201.2, L1201.1 (A1)
A_F-: C1201.2, F1202.2, L1201.3 (B1)
A_HC1_HOLD: Q1202.1 (G)
A_HC2_HOLD: Q1206.1 (G)
A_HC_G2: Q1204.1 (G), Q1205.3 (D), R1219.2, R1220.1
A_HC_OUT: D1203.2 (A), Q1203.2 (D), R1219.1, R1221.1
A_HC_PD: Q1202.3 (D), R1217.1
A_HC_PG: Q1203.1 (G), R1217.2, R1218.2
A_HC_X: Q1205.1 (G), Q1206.3 (D), R1221.2, R1222.1
A_IN+: F1201.1, F1203.1, J1201.1, X1201.1
A_IN-: F1202.1, F1204.1, J1202.1, X1203.1
A_KM_COIL: D1202.1 (K), D1203.1 (K), K1201.2 (COIL+), RV1204.1
A_KM_G1: Q1201.1 (G), R1215.2, R1216.1
A_KM_LO: K1201.3 (COIL-), Q1201.2 (D), Q1204.2 (D), RV1204.2
A_KP_G: Q1207.1 (G), R1223.2, R1224.1
A_KP_LO: D1204.1 (K), K1202.0 (COIL), Q1207.2 (D)
A_KP_Z: D1204.2 (A), D1205.2 (A)
A_MON1: R1201.1, RV1201.3 (MON)
A_MON2: R1212.2, RV1202.3 (MON)
A_MON3: D1201.1 (A), RV1203.3 (MON), U1201.2 (K)
A_MONA: D1201.3 (K), R1206.2, U1201.1 (A)
A_MR1: R1201.2, R1202.1
A_MR2: R1202.2, R1203.1
A_MR3: R1203.2, R1204.1
A_MR4: R1204.2, R1205.1
A_MR5: R1205.2, R1206.1
A_MS1: R1207.2, R1208.1
A_MS2: R1208.2, R1209.1
A_MS3: R1209.2, R1210.1
A_MS4: R1210.2, R1211.1
A_MS5: R1211.2, R1212.1
A_PRE_M: K1202.4 (P2), K1202.6 (P1)
A_PRE_R: K1202.2 (P2-), R1225.1
A_SH_N: RS1201.3 (SENSE1)
A_SH_P: RS1201.4 (SENSE2)
A_SP+: F1203.2, RV1201.1 (L), X1202.1
A_SP-: F1204.2, RV1202.1 (L), X1204.1
A_SPD_N: R1213.2, U1201.4 (C)
A_SPM: R1207.1, RV1201.2 (N), RV1202.2 (N), RV1203.1 (L)
A_X+: C1202.1, C1203.1, J1206.1, K1201.A1, K1202.8 (P1+), L1201.2 (A2)
A_X-: C1202.2, C1204.1, L1201.4 (B2), RS1201.1 (BOLT1)
FB_A_MAIN: D1208.1 (A), K1201.4 (AUX_NC), R1214.2
GND: C1205.2, K1201.1 (AUX_COM), Q1201.3 (S), Q1202.2 (S), Q1204.3 (S), Q1205.2 (S), Q1206.2 (S), Q1207.3 (S), R1216.2, R1220.2, R1222.2, R1224.2, R1234.2, R1235.2, R1236.2, U1202.4 (VSSP)
K_A_MAIN: D1202.2 (A), R1215.1
K_A_PRE: D1205.1 (K), K1202.1 (COIL), R1223.1
K_DISCH: D1207.1 (A), R1236.1
NTC_A_1: J1203.1, RT1201.1
NTC_A_2: J1203.2, RT1201.2
P1_BUS+: J1204.1, K1201.A2, R1225.2, R1226.1, R1228.1, R1243.1
P1_BUS-: C1207.2, C1208.2, C1209.2, D1206.1 (A), J1205.1, Q1208.3 (S), Q1209.2 (S), Q1212.2 (E), R1233.2, R1238.2, R1241.2, R1252.2, RS1201.2 (BOLT2), U1202.5 (VSSS)
PE: C1203.2, C1204.2, RV1203.2 (N)

Notes on the sheet:
TVT25751 x 3 (615 VDC, thermal link + monitor lead): MOV1 +/M, MOV2 -/M, MOV3 M/PE_T. Up,eff 3793 V pole-PE and pole-pole at In 3 kA (calc., <= 4.0 kV -> reinforced 6 kV / basic 4 kV, D-032); Imax 25 kA. Branch fuses ETI CH14x51 gPV 36 A 30 kA (L/R 2 ms). Monitor loop through both fuses and all thr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
SHUNT (- POLE) + SHUNT NTC
MAIN CONTACTOR: COIL DRIVE + FEEDBACK
PASSIVE BLEEDER + BOARD CONNECTION POINTS
CHASSIS-MOUNTED. 135 A port: gPV 160 A 1000 V DC in each pole, derated 124 A (fuses in the INLET air path, PD3: terminals / fuse bases only, creepage to PE >= 16.0 mm IIIa, IC-18/IC-21).
X 2 x 2.2 uF film (RFQ: impulse >= 4.5 kV, PA-07), CM choke (CUSTOM), Y1 4.7 nF pole-PE (1500 VDC rated). Y capacitors are declared HV-PE crossings.
ON-BOARD SURGE PROTECTION: VARISTOR Y (IC-01, IC-12)
EMI FILTER
G7L-2A-X, poles in series, normal polarity = current 8 -> 2 (terminal -> bus). K_A_PRE feeds the coil and gates its IRFL214 low side; S2M + SMBJ33A across the coil (37-42 V, Omron p5). R_pre 220 ohm Miba RST 200 (RFQ, pulse-rated). Complete at |dV| <= 10 V after the VA/VAX null; abort below 0.8 x V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
TPSI3050 EN = K_DISCH OR FB_A_MAIN (2 x BAS16): powered = BSS138 holds the SiC gate low. Unpowered = the bus biases the gate (10 M, 15 V zener) -> 2 x 300 ohm Miba RST 200 discharge the bus. FB is high while the contactor is closed (or welded), so an E-stop or a lost K_DISCH cannot discharge a live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
PRECHARGE RELAY + RESISTOR
CSM2F-8518 100 uOhm, busbar-mounted. Kelvin test points to the IA/IB amplifier. Positive current = power into the module at this port. NTC on the shunt (reinforced pad) -> SYS-IO-AUX NTC input: firmware TCR compensation.
DIS_G charges 1 uF through 4.7 M; a MMBT3906 compares it with DIS_G/2 (1 M / 1 M, also the gate pull- down) and fires the MMBT3906/MMBT3904 latch: gate clamped to 0.75 V after 2.4-5.1 s (needed <= 1.8 s), held by the bias current until K_DISCH returns (BSS138 resets it). Thermostat KSD301-class (cl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
Channel 1: HOLD1 -> BSS138 -> IRFR9214 high side from the port +24V (not cut by E-stop) -> S2M -> coil+. Channel 2: IRFL214 low side coil- -> GND, gate fed from the channel-1 output (10 k / 22 k) and clamped off by a BSS138 unless HOLD2: it can only conduct while channel 1 conducts, so no flyback e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
10 x 47 k 2512 1 W (100 V each at 1000 V): back-up discharge, 2.4 W at 1000 V. REDCUBE studs: bus +/- to the power cells, terminal-side tap.
HVC43-250A-24MC, + pole, bidirectional (TDK p2). Opens at zero current in normal operation; cut-off 450 A @ 1000 V once. K_A_MAIN feeds coil+ (S2M) AND gates the IRFL214 low side: two switches in the path. S10K30 directly across the coil = the only flyback path (>= 54 V down to drop-out; TDK p7 >= 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
DISCHARGE TIME LIMIT + THERMAL CUT-OFF (HV SIDE, NEEDS NO 24 V)
HOLD-CLOSED POWER STAGE (2 INDEPENDENT CHANNELS)
TERMINALS, FUSES (PV-TYPE PORT)
FAIL-SAFE ACTIVE DISCHARGE, INHIBITED WHILE THE CONTACTOR IS CLOSED
