vectivolt/PCM/hardware/DAB60/sheets/13_portA_sense.kicad_sch

## KiCad design hardware/DAB60/sheets/13_portA_sense.kicad_sch (2026-10-04)

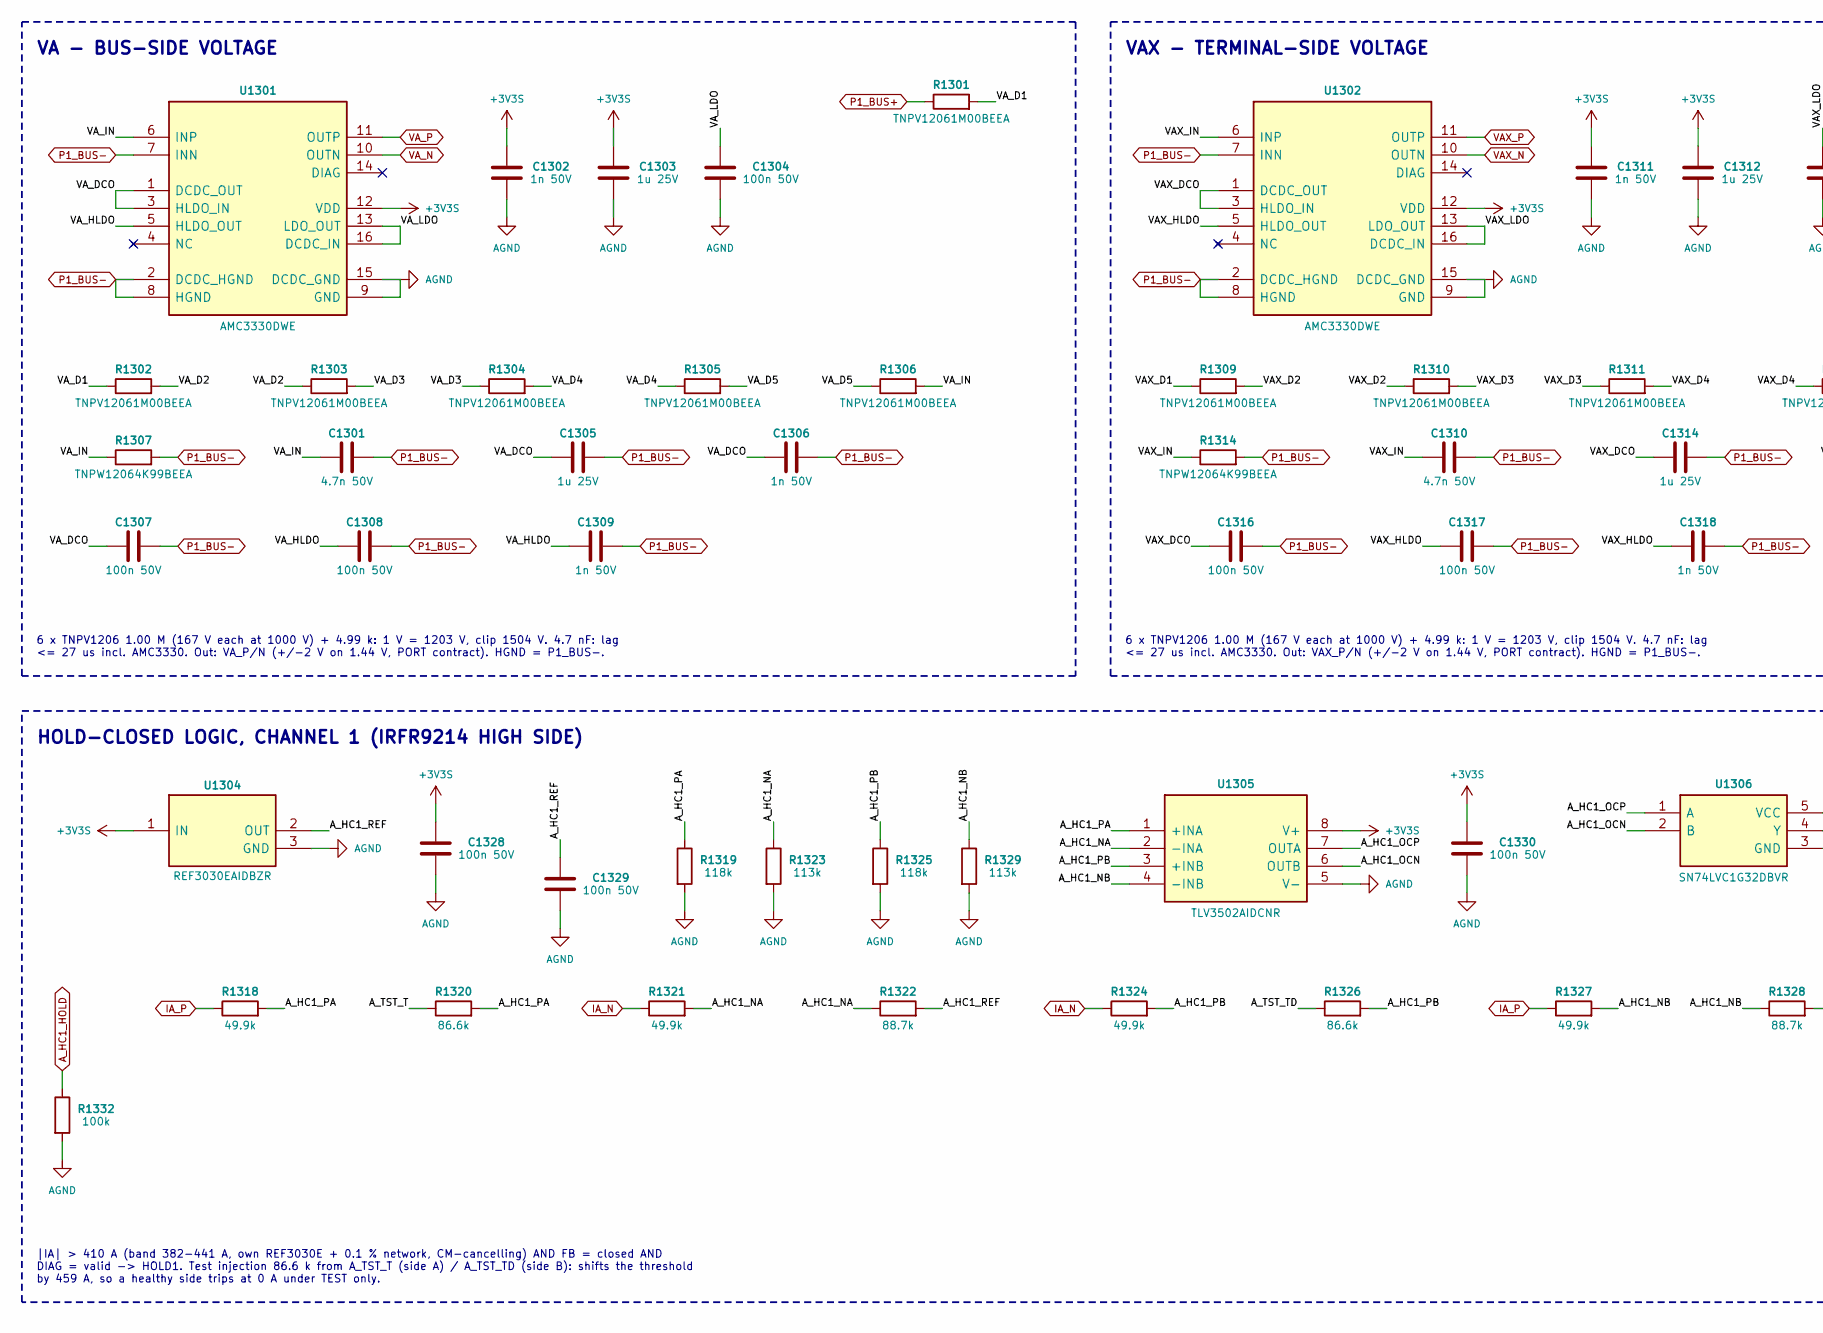
[picture p251: schematic 13_portA_sense.kicad_sch, part in row 1, column 1]

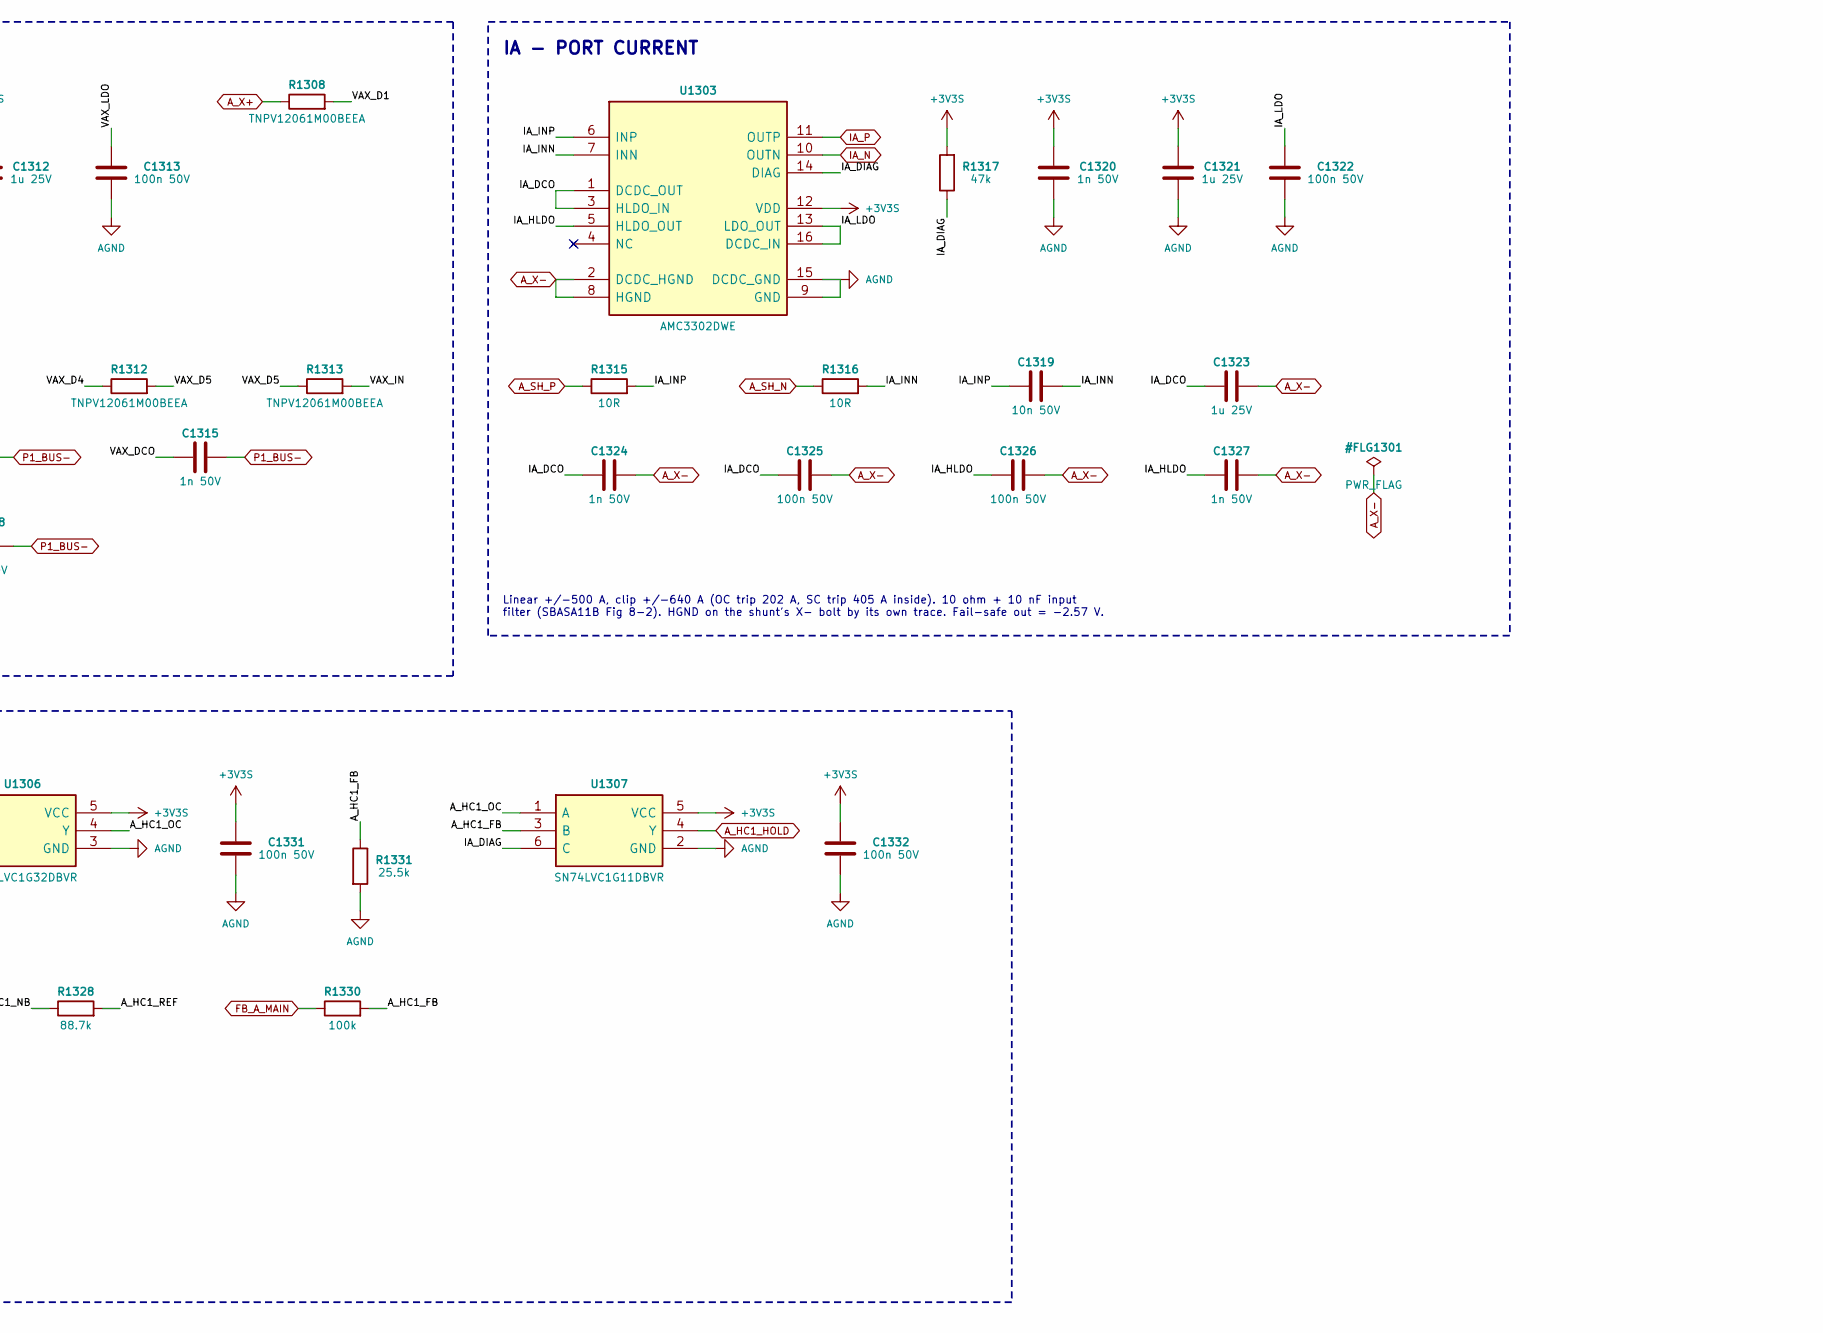
[picture p252: schematic 13_portA_sense.kicad_sch, part in row 1, column 2]

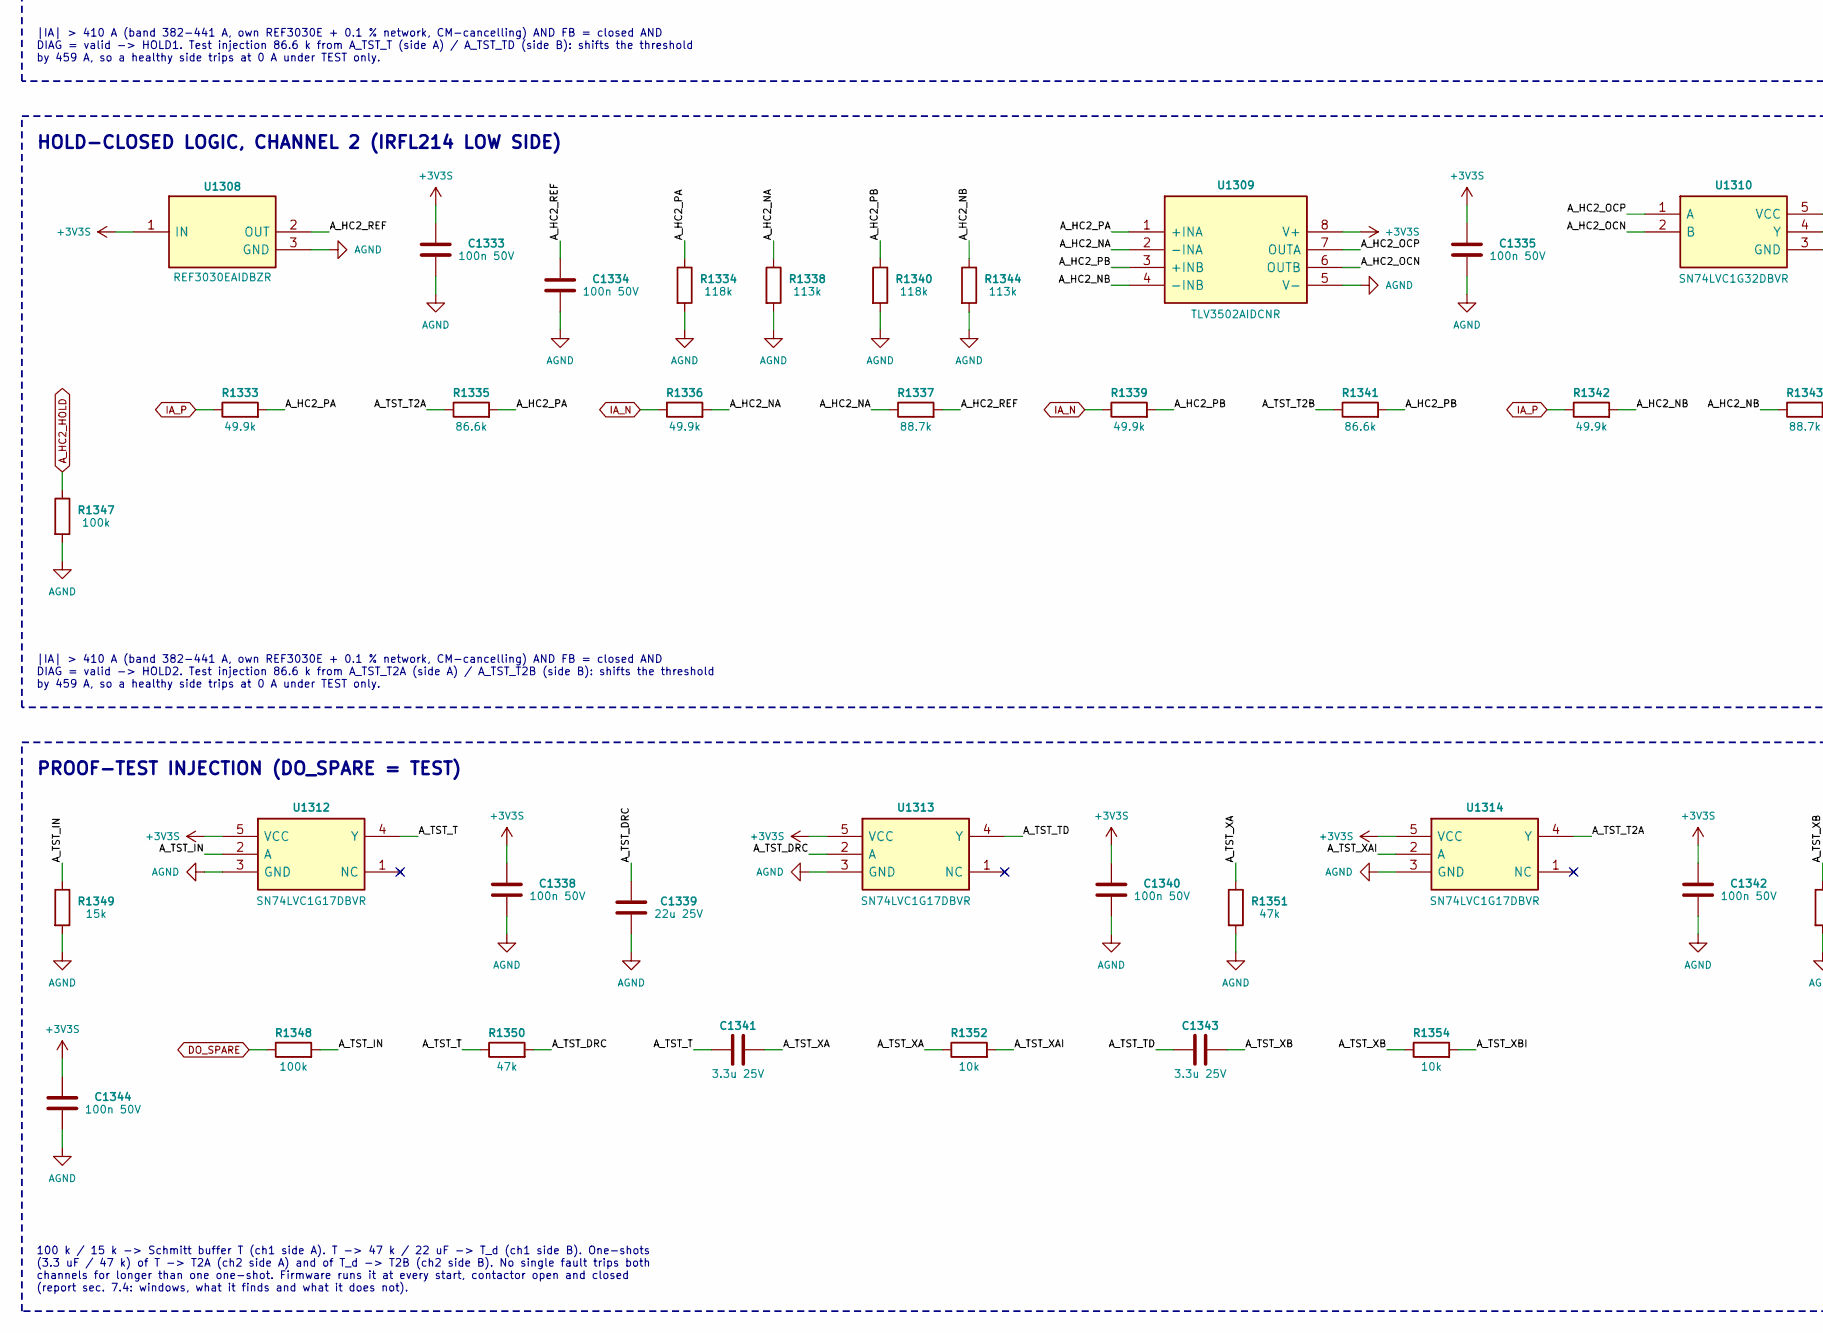
[picture p253: schematic 13_portA_sense.kicad_sch, part in row 2, column 1]

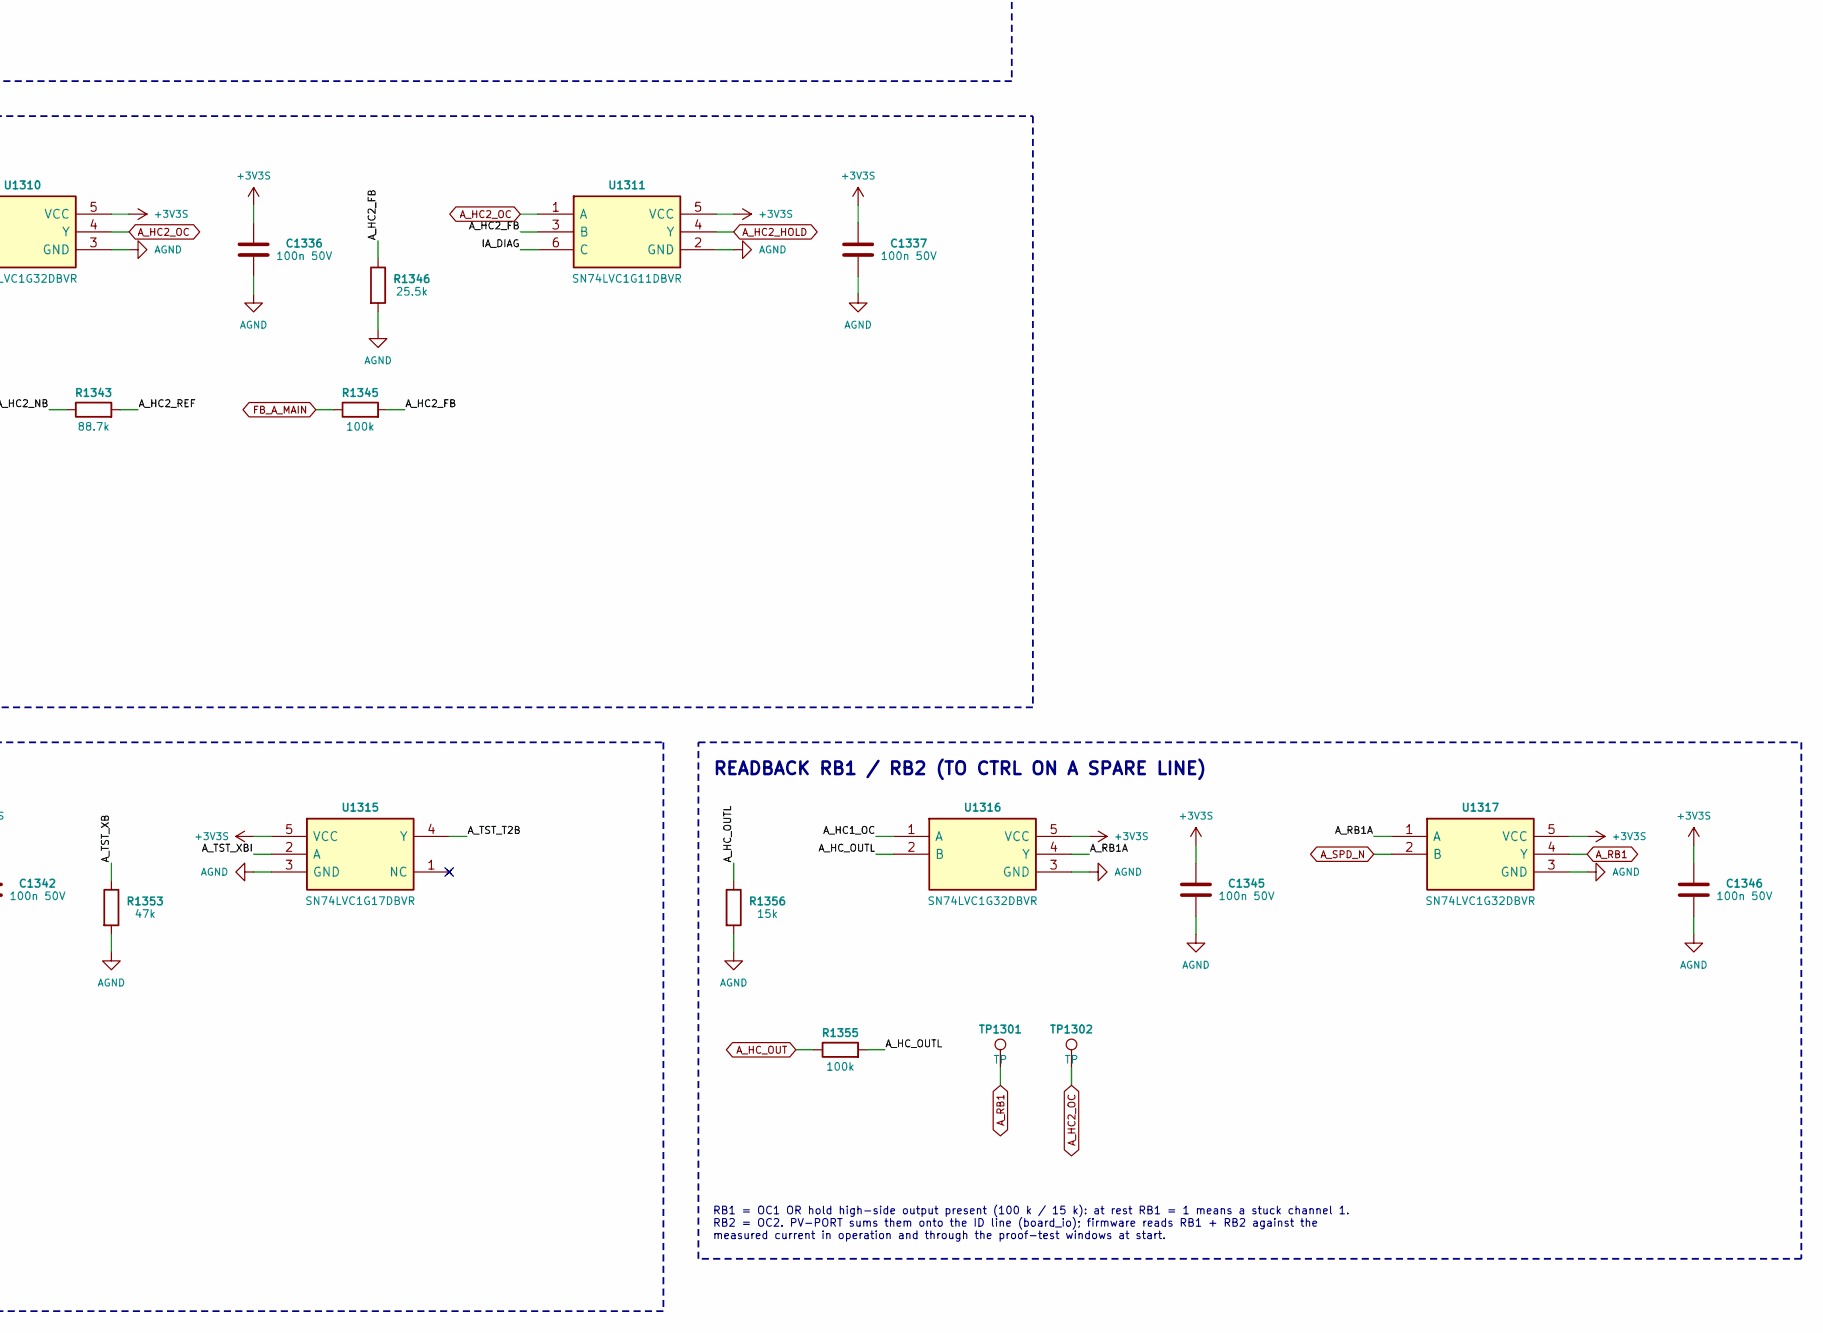
[picture p254: schematic 13_portA_sense.kicad_sch, part in row 2, column 2]

Parts:
C1301, C1310: 4.7n 50V
C1302, C1306, C1309, C1311, C1315, C1318, C1320, C1324, C1327: 1n 50V
C1303, C1305, C1312, C1314, C1321, C1323: 1u 25V
C1304, C1307, C1308, C1313, C1316, C1317, C1322, C1325, C1326, C1328, C1329, C1330, C1331, C1332, C1333, C1334, C1335, C1336, C1337, C1338, C1340, C1342, C1344, C1345, C1346: 100n 50V
C1319: 10n 50V
C1339: 22u 25V
C1341, C1343: 3.3u 25V
R1301, R1302, R1303, R1304, R1305, R1306, R1308, R1309, R1310, R1311, R1312, R1313: TNPV12061M00BEEA; MPN TNPV12061M00BEEA
R1307, R1314: TNPW12064K99BEEA; MPN TNPW12064K99BEEA
R1315, R1316: 10R
R1317, R1350, R1351, R1353: 47k
R1318, R1321, R1324, R1327, R1333, R1336, R1339, R1342: 49.9k
R1319, R1325, R1334, R1340: 118k
R1320, R1326, R1335, R1341: 86.6k
R1322, R1328, R1337, R1343: 88.7k
R1323, R1329, R1338, R1344: 113k
R1330, R1332, R1345, R1347, R1348, R1355: 100k
R1331, R1346: 25.5k
R1349, R1356: 15k
R1352, R1354: 10k
TP1301, TP1302: TP
U1301, U1302: AMC3330DWE; MPN AMC3330DWE
U1303: AMC3302DWE; MPN AMC3302DWE
U1304, U1308: REF3030EAIDBZR; MPN REF3030EAIDBZR
U1305, U1309: TLV3502AIDCNR; MPN TLV3502AIDCNR
U1306, U1310, U1316, U1317: SN74LVC1G32DBVR; MPN SN74LVC1G32DBVR
U1307, U1311: SN74LVC1G11DBVR; MPN SN74LVC1G11DBVR
U1312, U1313, U1314, U1315: SN74LVC1G17DBVR; MPN SN74LVC1G17DBVR

Connections:
+3V3S: C1302.1, C1303.1, C1311.1, C1312.1, C1320.1, C1321.1, C1328.1, C1330.1, C1331.1, C1332.1, C1333.1, C1335.1, C1336.1, C1337.1, C1338.1, C1340.1, C1342.1, C1344.1, C1345.1, C1346.1, R1317.2, U1301.12 (VDD), U1302.12 (VDD), U1303.12 (VDD), U1304.1 (IN), U1305.8 (V+), U1306.5 (VCC), U1307.5 (VCC), U1308.1 (IN), U1309.8 (V+), U1310.5 (VCC), U1311.5 (VCC), U1312.5 (VCC), U1313.5 (VCC), U1314.5 (VCC), U1315.5 (VCC), U1316.5 (VCC), U1317.5 (VCC)
AGND: C1302.2, C1303.2, C1304.2, C1311.2, C1312.2, C1313.2, C1320.2, C1321.2, C1322.2, C1328.2, C1329.2, C1330.2, C1331.2, C1332.2, C1333.2, C1334.2, C1335.2, C1336.2, C1337.2, C1338.2, C1339.2, C1340.2, C1342.2, C1344.2, C1345.2, C1346.2, R1319.2, R1323.2, R1325.2, R1329.2, R1331.2, R1332.2, R1334.2, R1338.2, R1340.2, R1344.2, R1346.2, R1347.2, R1349.2, R1351.2, R1353.2, R1356.2, U1301.9 (GND), U1301.15 (DCDC_GND), U1302.9 (GND), U1302.15 (DCDC_GND), U1303.9 (GND), U1303.15 (DCDC_GND), U1304.3 (GND), U1305.5 (V-), U1306.3 (GND), U1307.2 (GND), U1308.3 (GND), U1309.5 (V-), U1310.3 (GND), U1311.2 (GND), U1312.3 (GND), U1313.3 (GND), U1314.3 (GND), U1315.3 (GND), U1316.3 (GND), U1317.3 (GND)
A_HC1_FB: R1330.2, R1331.1, U1307.3 (B)
A_HC1_HOLD: R1332.1, U1307.4 (Y)
A_HC1_NA: R1321.2, R1322.1, R1323.1, U1305.2 (-INA)
A_HC1_NB: R1327.2, R1328.1, R1329.1, U1305.4 (-INB)
A_HC1_OC: U1306.4 (Y), U1307.1 (A), U1316.1 (A)
A_HC1_OCN: U1305.6 (OUTB), U1306.2 (B)
A_HC1_OCP: U1305.7 (OUTA), U1306.1 (A)
A_HC1_PA: R1318.2, R1319.1, R1320.2, U1305.1 (+INA)
A_HC1_PB: R1324.2, R1325.1, R1326.2, U1305.3 (+INB)
A_HC1_REF: C1329.1, R1322.2, R1328.2, U1304.2 (OUT)
A_HC2_FB: R1345.2, R1346.1, U1311.3 (B)
A_HC2_HOLD: R1347.1, U1311.4 (Y)
A_HC2_NA: R1336.2, R1337.1, R1338.1, U1309.2 (-INA)
A_HC2_NB: R1342.2, R1343.1, R1344.1, U1309.4 (-INB)
A_HC2_OC: TP1302.1, U1310.4 (Y), U1311.1 (A)
A_HC2_OCN: U1309.6 (OUTB), U1310.2 (B)
A_HC2_OCP: U1309.7 (OUTA), U1310.1 (A)
A_HC2_PA: R1333.2, R1334.1, R1335.2, U1309.1 (+INA)
A_HC2_PB: R1339.2, R1340.1, R1341.2, U1309.3 (+INB)
A_HC2_REF: C1334.1, R1337.2, R1343.2, U1308.2 (OUT)
A_HC_OUT: R1355.1
A_HC_OUTL: R1355.2, R1356.1, U1316.2 (B)
A_RB1: TP1301.1, U1317.4 (Y)
A_RB1A: U1316.4 (Y), U1317.1 (A)
A_SH_N: R1316.1
A_SH_P: R1315.1
A_SPD_N: U1317.2 (B)
A_TST_DRC: C1339.1, R1350.2, U1313.2 (A)
A_TST_IN: R1348.2, R1349.1, U1312.2 (A)
A_TST_T: C1341.1, R1320.1, R1350.1, U1312.4 (Y)
A_TST_T2A: R1335.1, U1314.4 (Y)
A_TST_T2B: R1341.1, U1315.4 (Y)
A_TST_TD: C1343.1, R1326.1, U1313.4 (Y)
A_TST_XA: C1341.2, R1351.1, R1352.1
A_TST_XAI: R1352.2, U1314.2 (A)
A_TST_XB: C1343.2, R1353.1, R1354.1
A_TST_XBI: R1354.2, U1315.2 (A)
A_X+: R1308.1
A_X-: C1323.2, C1324.2, C1325.2, C1326.2, C1327.2, U1303.2 (DCDC_HGND), U1303.8 (HGND)
DO_SPARE: R1348.1
FB_A_MAIN: R1330.1, R1345.1
IA_DCO: C1323.1, C1324.1, C1325.1, U1303.1 (DCDC_OUT), U1303.3 (HLDO_IN)
IA_DIAG: R1317.1, U1303.14 (DIAG), U1307.6 (C), U1311.6 (C)
IA_HLDO: C1326.1, C1327.1, U1303.5 (HLDO_OUT)
IA_INN: C1319.2, R1316.2, U1303.7 (INN)
IA_INP: C1319.1, R1315.2, U1303.6 (INP)
IA_LDO: C1322.1, U1303.13 (LDO_OUT), U1303.16 (DCDC_IN)
IA_N: R1321.1, R1324.1, R1336.1, R1339.1, U1303.10 (OUTN)
IA_P: R1318.1, R1327.1, R1333.1, R1342.1, U1303.11 (OUTP)
P1_BUS+: R1301.1
P1_BUS-: C1301.2, C1305.2, C1306.2, C1307.2, C1308.2, C1309.2, C1310.2, C1314.2, C1315.2, C1316.2, C1317.2, C1318.2, R1307.2, R1314.2, U1301.2 (DCDC_HGND), U1301.7 (INN), U1301.8 (HGND), U1302.2 (DCDC_HGND), U1302.7 (INN), U1302.8 (HGND)
VAX_D1: R1308.2, R1309.1
VAX_D2: R1309.2, R1310.1
VAX_D3: R1310.2, R1311.1
VAX_D4: R1311.2, R1312.1
VAX_D5: R1312.2, R1313.1
VAX_DCO: C1314.1, C1315.1, C1316.1, U1302.1 (DCDC_OUT), U1302.3 (HLDO_IN)
VAX_HLDO: C1317.1, C1318.1, U1302.5 (HLDO_OUT)
VAX_IN: C1310.1, R1313.2, R1314.1, U1302.6 (INP)
VAX_LDO: C1313.1, U1302.13 (LDO_OUT), U1302.16 (DCDC_IN)
VAX_N: U1302.10 (OUTN)
VAX_P: U1302.11 (OUTP)
VA_D1: R1301.2, R1302.1
VA_D2: R1302.2, R1303.1
VA_D3: R1303.2, R1304.1
VA_D4: R1304.2, R1305.1
VA_D5: R1305.2, R1306.1
VA_DCO: C1305.1, C1306.1, C1307.1, U1301.1 (DCDC_OUT), U1301.3 (HLDO_IN)
VA_HLDO: C1308.1, C1309.1, U1301.5 (HLDO_OUT)
VA_IN: C1301.1, R1306.2, R1307.1, U1301.6 (INP)
VA_LDO: C1304.1, U1301.13 (LDO_OUT), U1301.16 (DCDC_IN)
VA_N: U1301.10 (OUTN)
VA_P: U1301.11 (OUTP)

Notes on the sheet:
READBACK RB1 / RB2 (TO CTRL ON A SPARE LINE)
HOLD-CLOSED LOGIC, CHANNEL 1 (IRFR9214 HIGH SIDE)
HOLD-CLOSED LOGIC, CHANNEL 2 (IRFL214 LOW SIDE)
VAX - TERMINAL-SIDE VOLTAGE
IA - PORT CURRENT
|IA| > 410 A (band 382-441 A, own REF3030E + 0.1 % network, CM-cancelling) AND FB = closed AND DIAG = valid -> HOLD1. Test injection 86.6 k from A_TST_T (side A) / A_TST_TD (side B): shifts the threshold by 459 A, so a healthy side trips at 0 A under TEST only.
Linear +/-500 A, clip +/-640 A (OC trip 202 A, SC trip 405 A inside). 10 ohm + 10 nF input filter (SBASA11B Fig 8-2). HGND on the shunt's X- bolt by its own trace. Fail-safe out = -2.57 V.
VA - BUS-SIDE VOLTAGE
6 x TNPV1206 1.00 M (167 V each at 1000 V) + 4.99 k: 1 V = 1203 V, clip 1504 V. 4.7 nF: lag <= 27 us incl. AMC3330. Out: VAX_P/N (+/-2 V on 1.44 V, PORT contract). HGND = P1_BUS-.
RB1 = OC1 OR hold high-side output present (100 k / 15 k): at rest RB1 = 1 means a stuck channel 1. RB2 = OC2. PV-PORT sums them onto the ID line (board_io); firmware reads RB1 + RB2 against the measured current in operation and through the proof-test windows at start.
100 k / 15 k -> Schmitt buffer T (ch1 side A). T -> 47 k / 22 uF -> T_d (ch1 side B). One-shots (3.3 uF / 47 k) of T -> T2A (ch2 side A) and of T_d -> T2B (ch2 side B). No single fault trips both channels for longer than one one-shot. Firmware runs it at every start, contactor open and closed (repo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
PROOF-TEST INJECTION (DO_SPARE = TEST)
|IA| > 410 A (band 382-441 A, own REF3030E + 0.1 % network, CM-cancelling) AND FB = closed AND DIAG = valid -> HOLD2. Test injection 86.6 k from A_TST_T2A (side A) / A_TST_T2B (side B): shifts the threshold by 459 A, so a healthy side trips at 0 A under TEST only.
6 x TNPV1206 1.00 M (167 V each at 1000 V) + 4.99 k: 1 V = 1203 V, clip 1504 V. 4.7 nF: lag <= 27 us incl. AMC3330. Out: VA_P/N (+/-2 V on 1.44 V, PORT contract). HGND = P1_BUS-.
