vectivolt/PCM/hardware/DAB60/sheets/14_portB_power.kicad_sch

## KiCad design hardware/DAB60/sheets/14_portB_power.kicad_sch (2026-10-04)

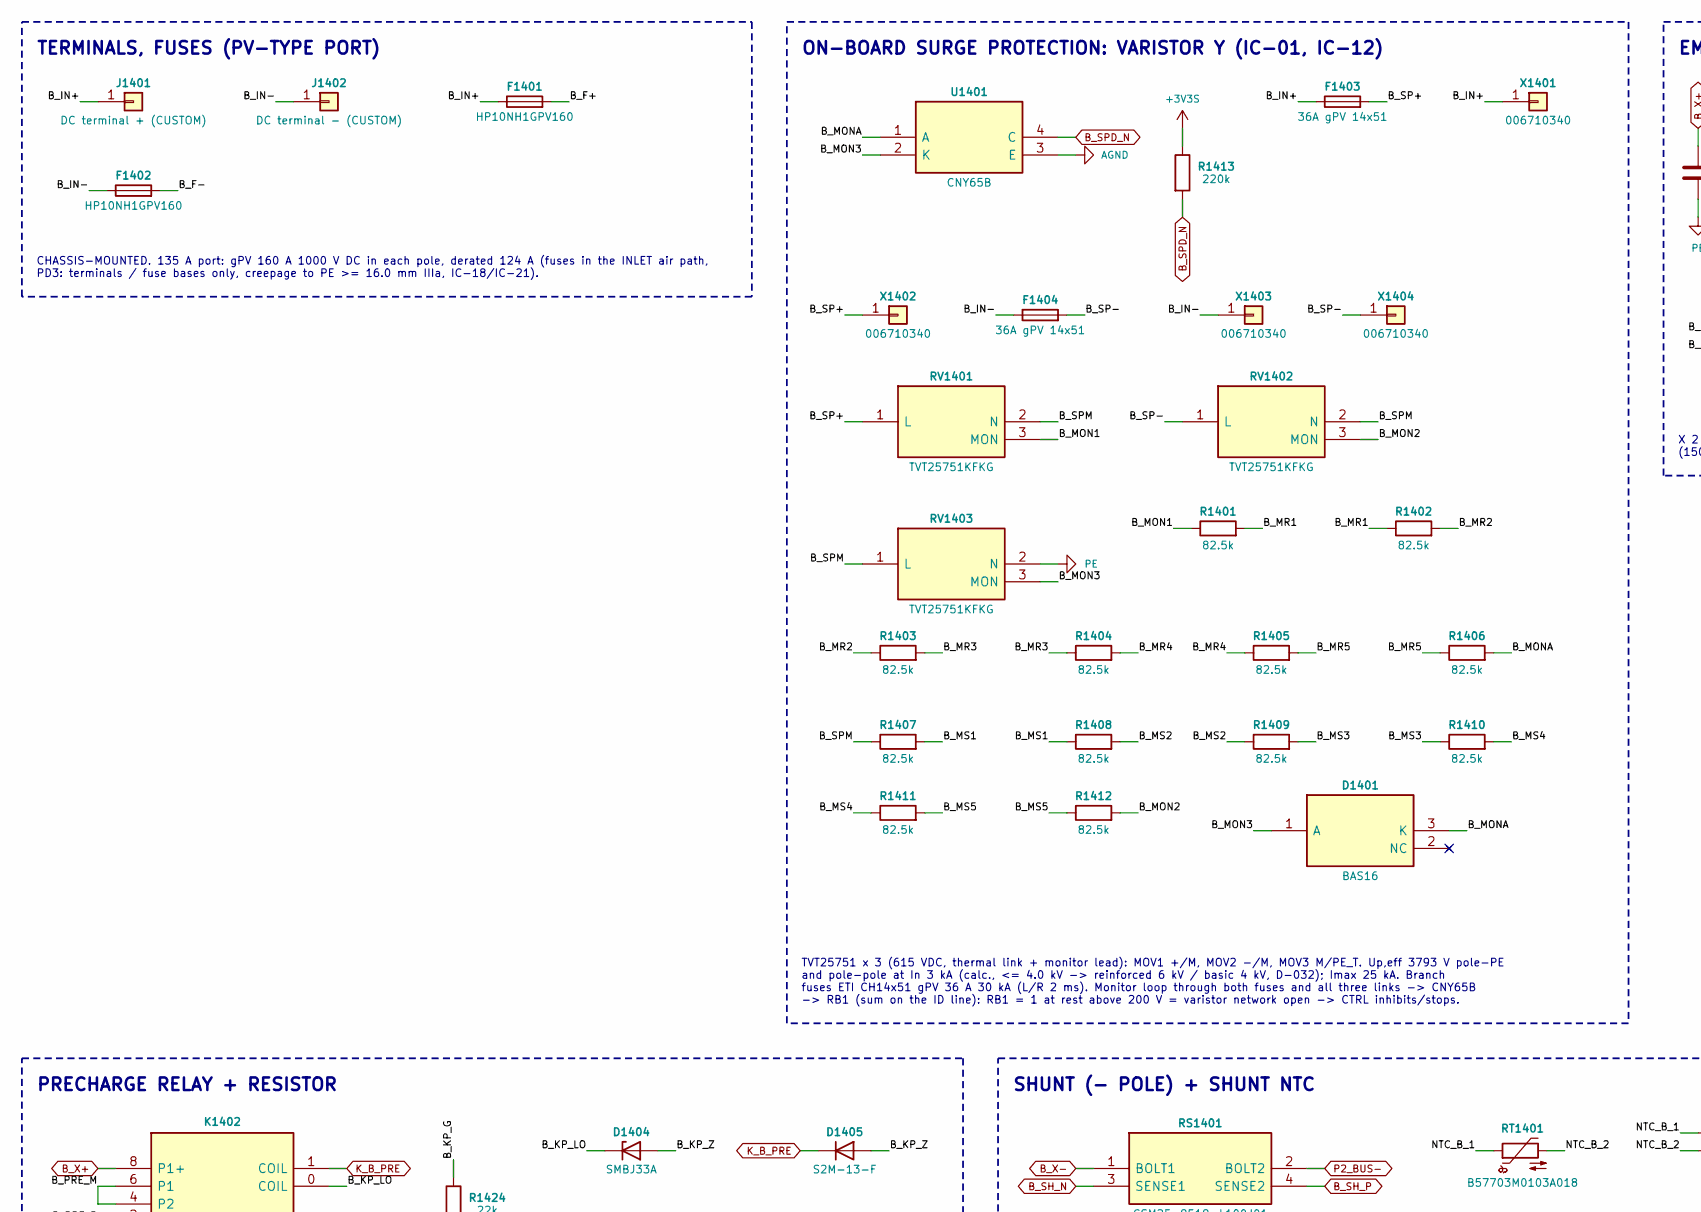
[picture p255: schematic 14_portB_power.kicad_sch, part in row 1, column 1]

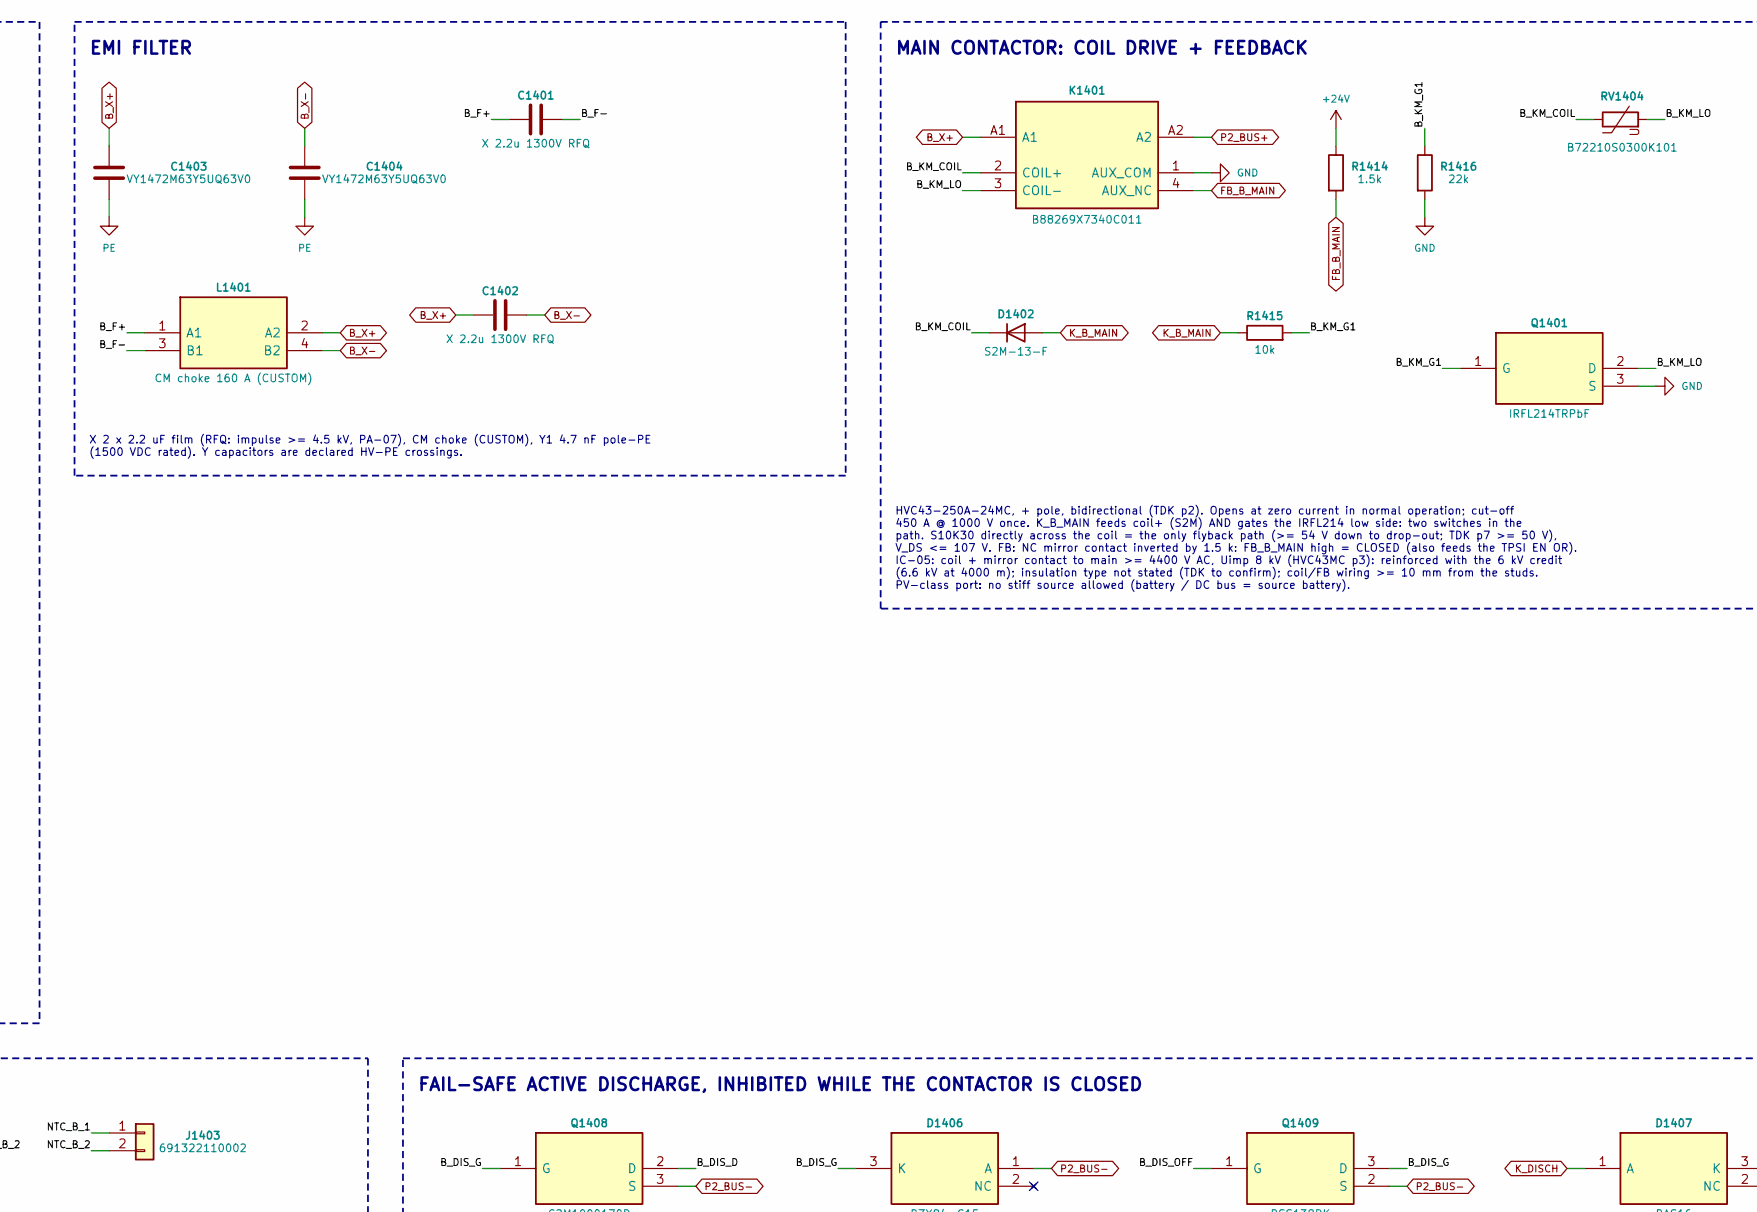
[picture p256: schematic 14_portB_power.kicad_sch, part in row 1, column 2]

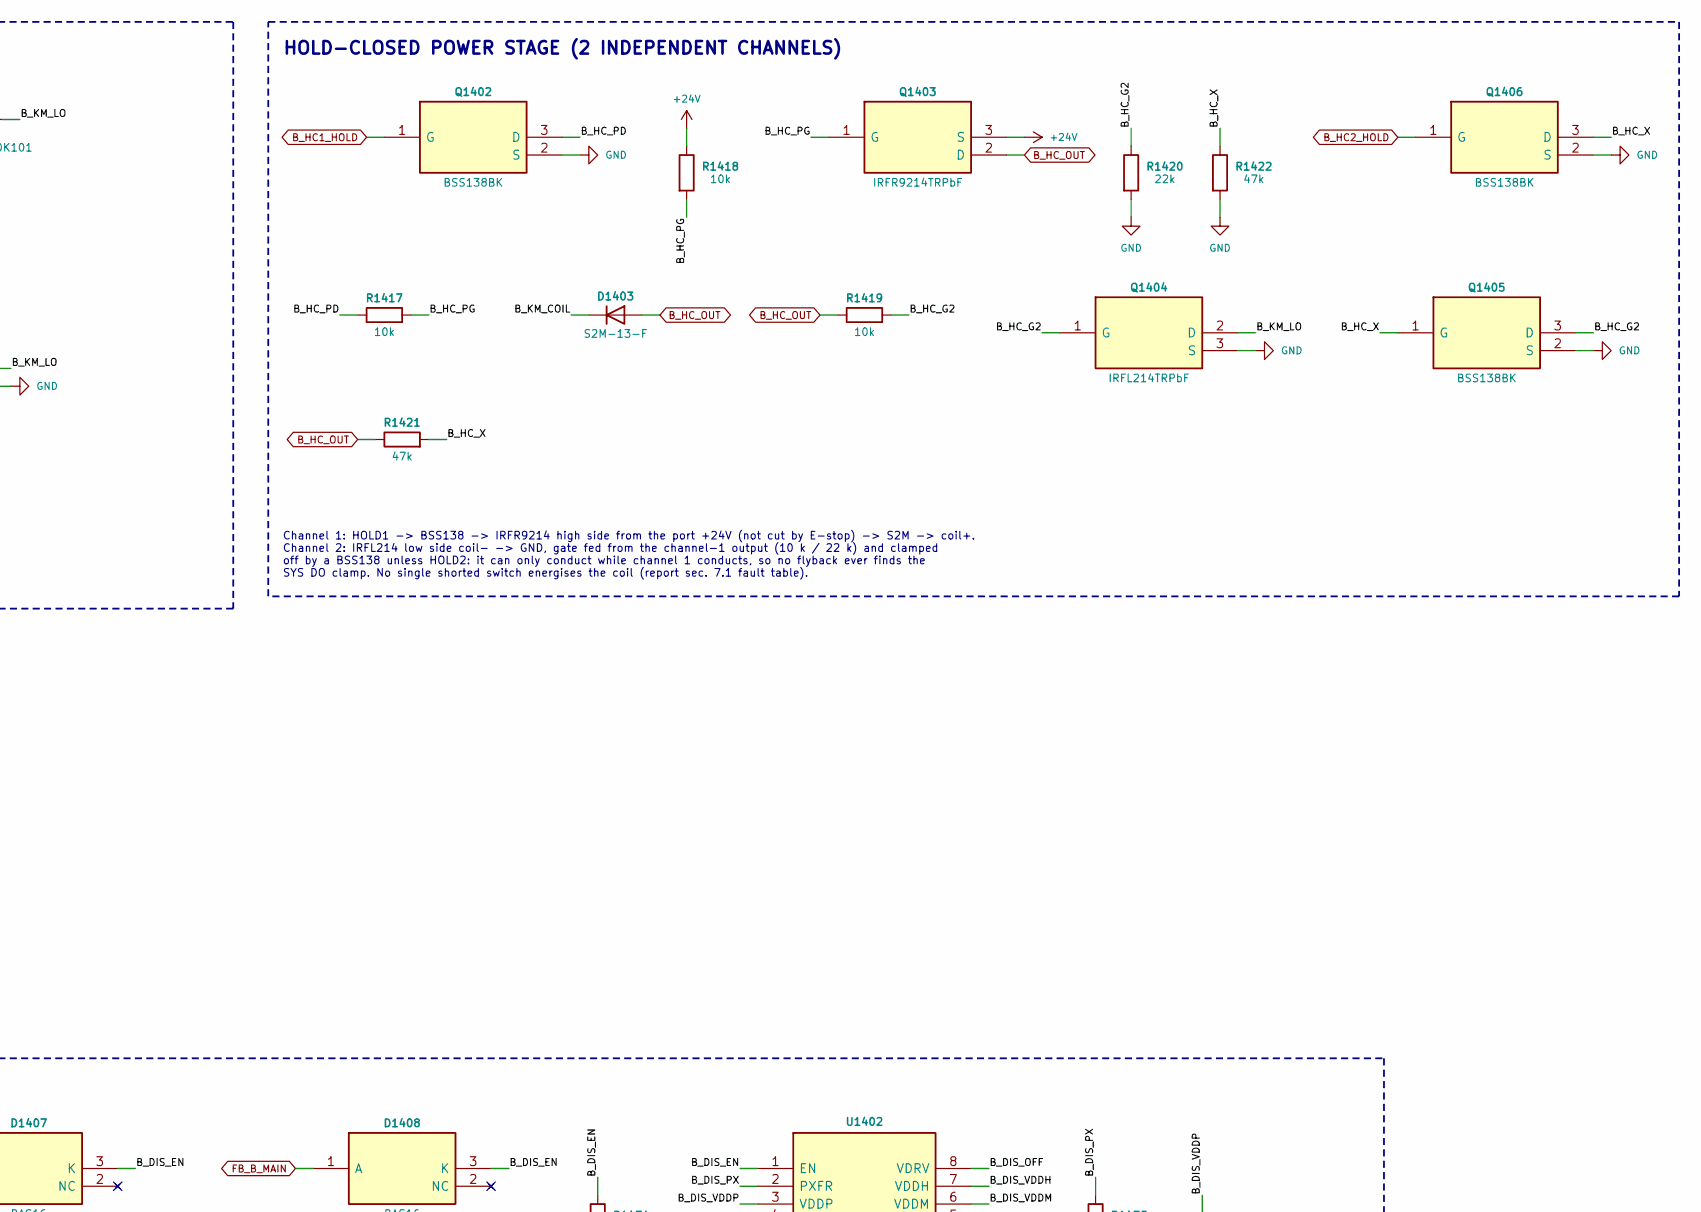
[picture p257: schematic 14_portB_power.kicad_sch, part in row 1, column 3]

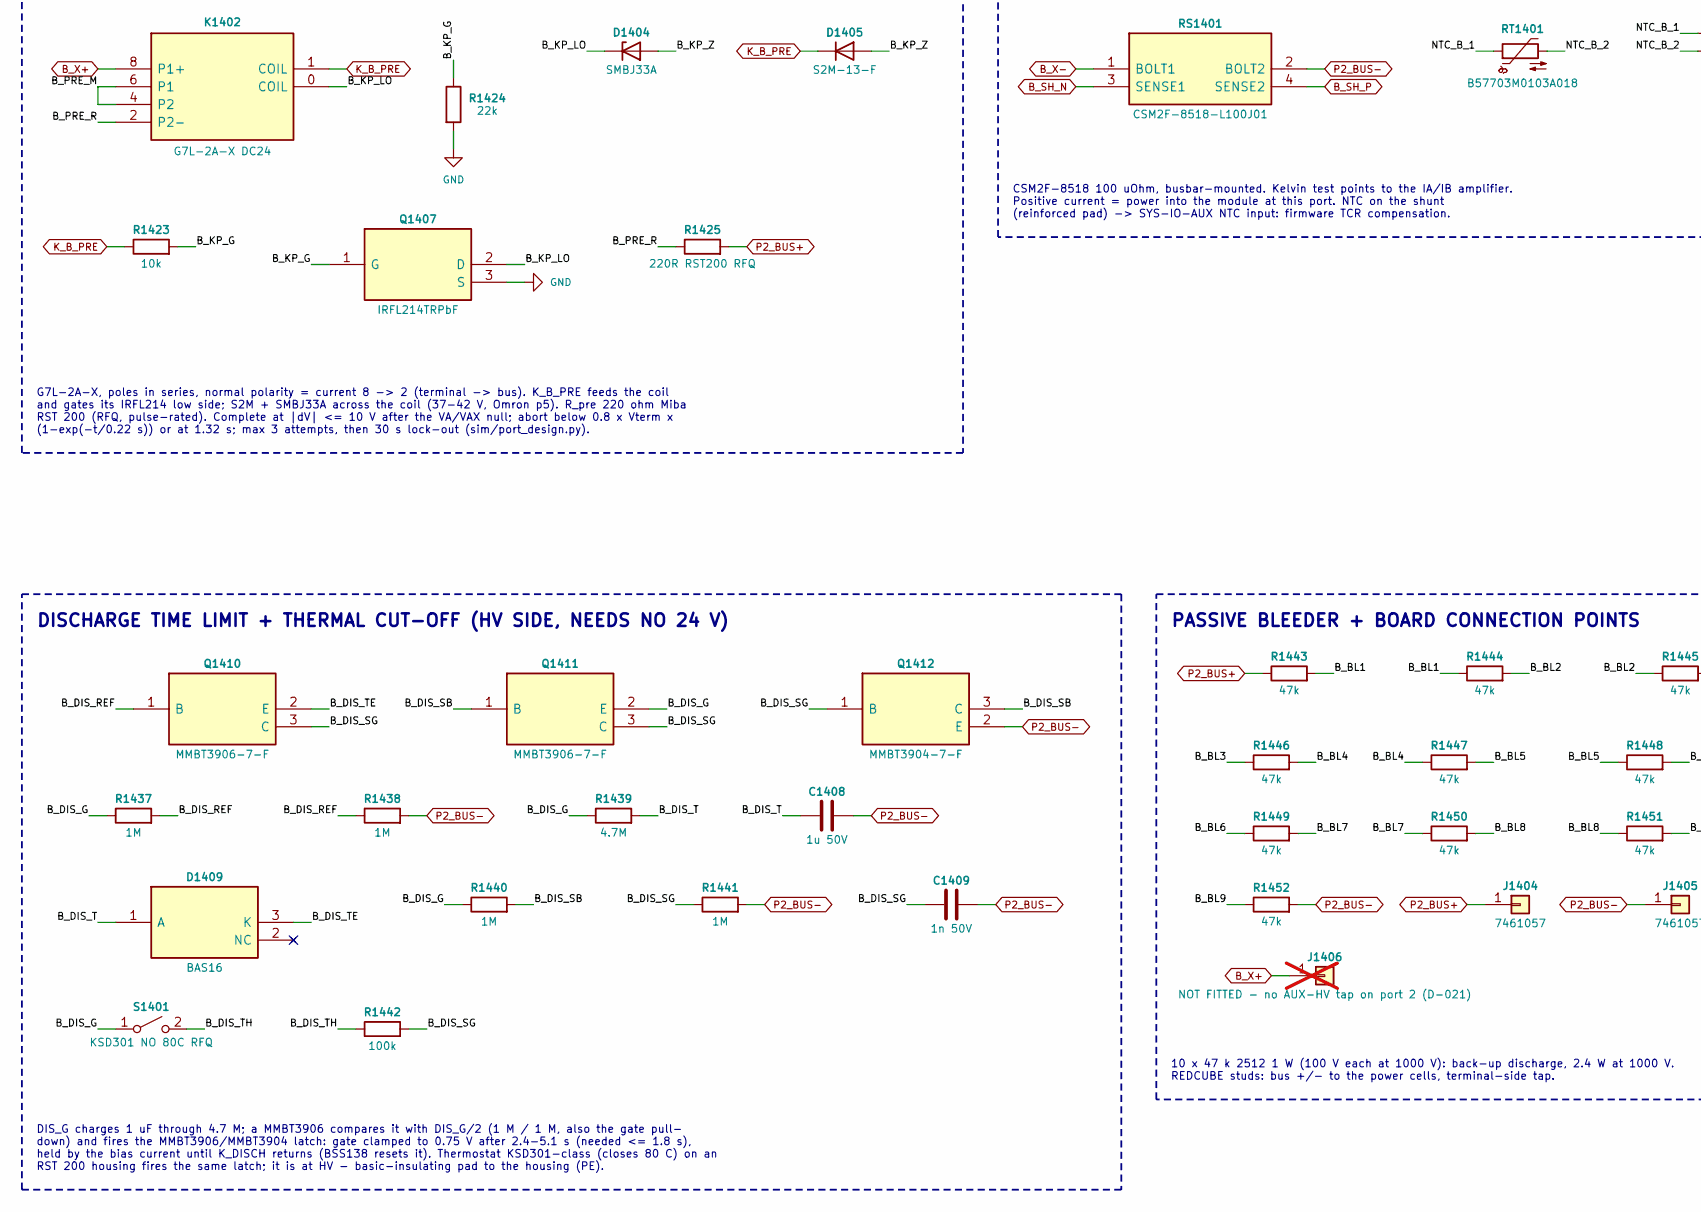
[picture p258: schematic 14_portB_power.kicad_sch, part in row 2, column 1]

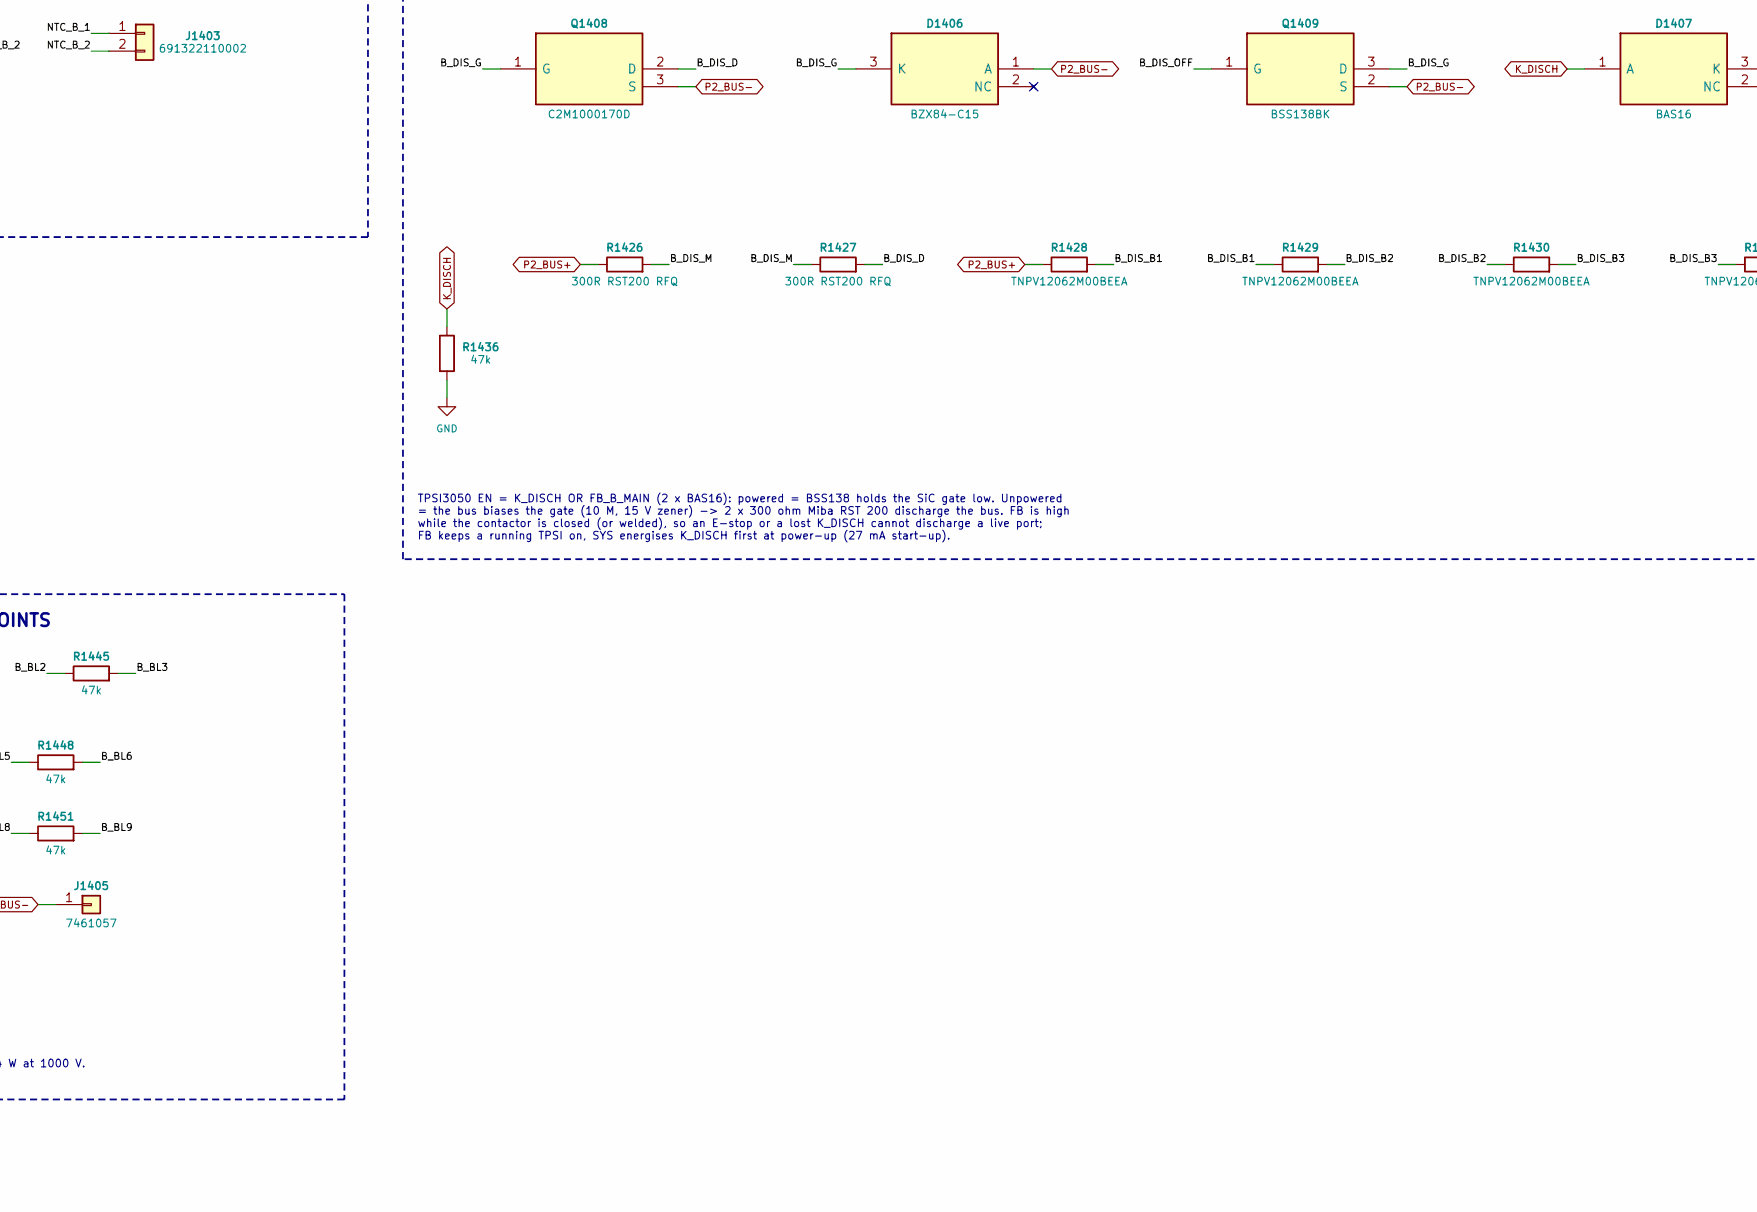
[picture p259: schematic 14_portB_power.kicad_sch, part in row 2, column 2]

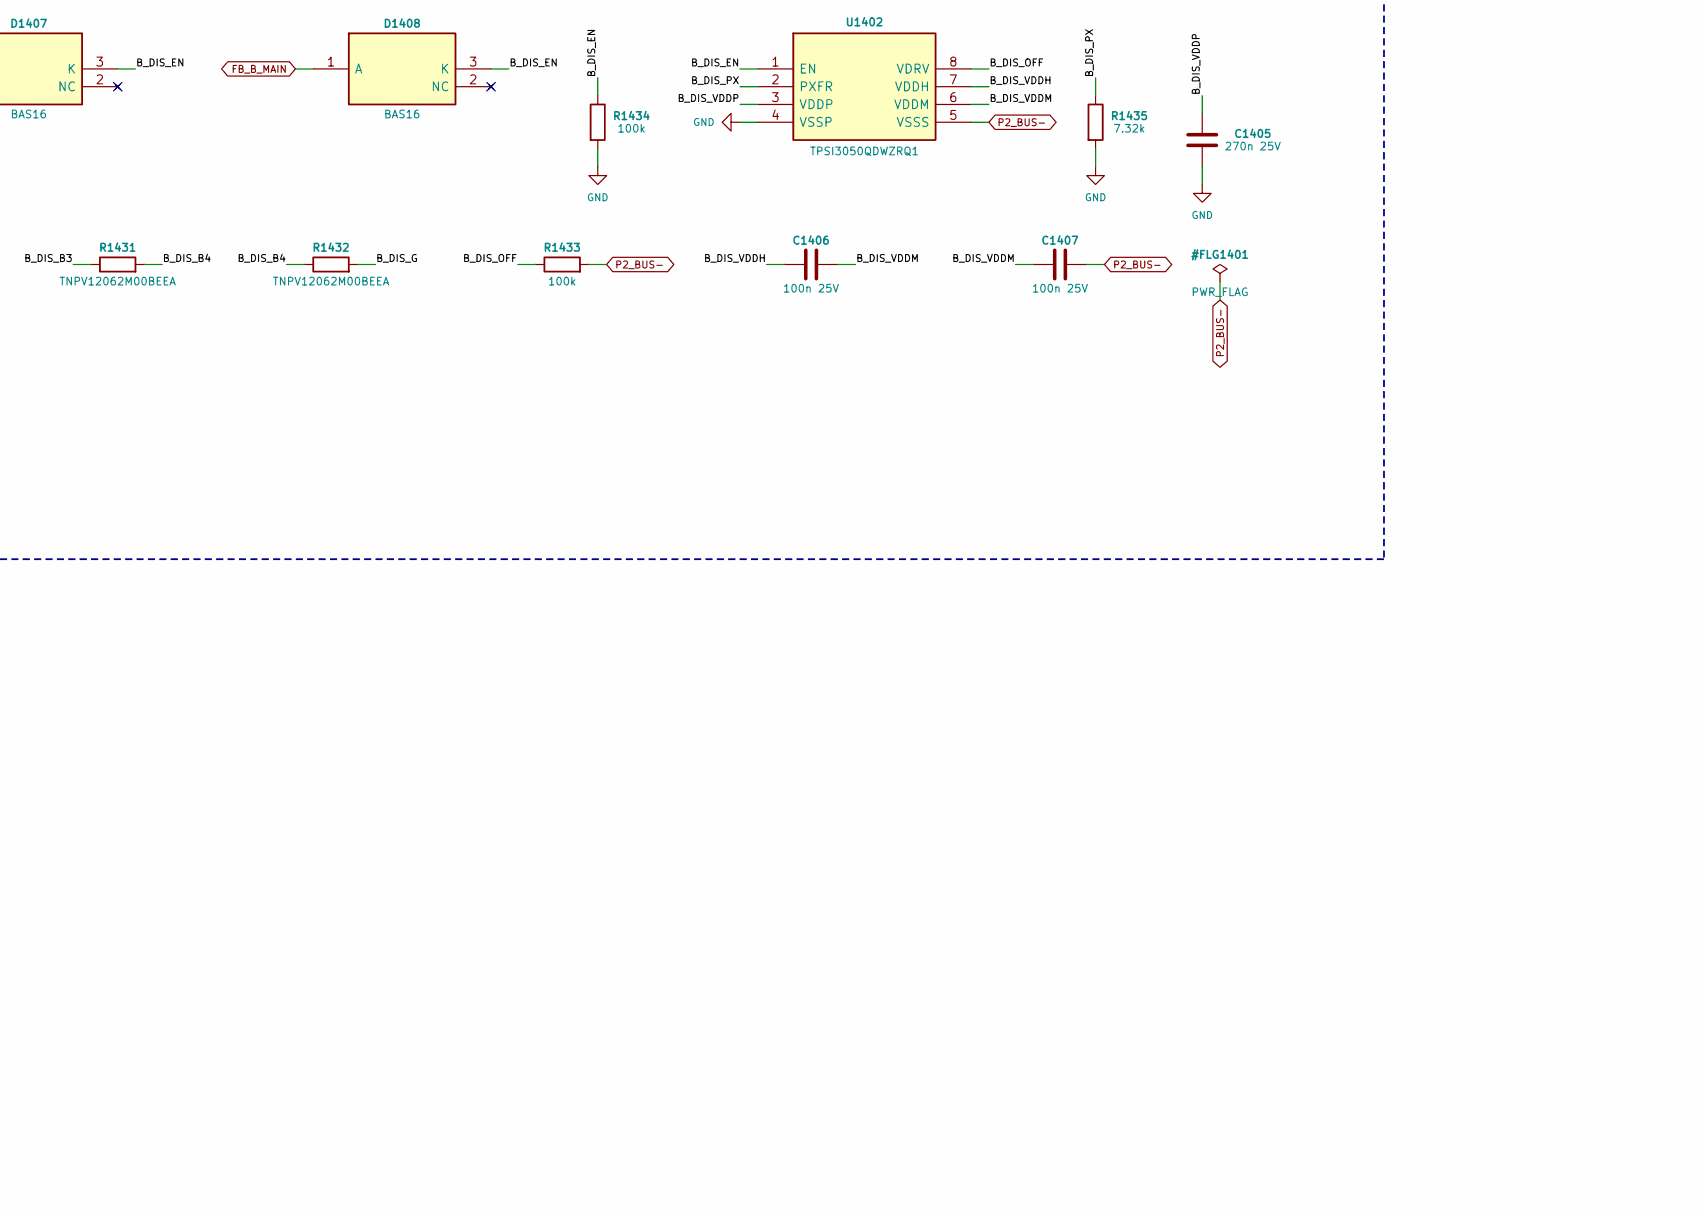
[picture p260: schematic 14_portB_power.kicad_sch, part in row 2, column 3]

Parts:
C1401, C1402: X 2.2u 1300V RFQ
C1403, C1404: VY1472M63Y5UQ63V0; MPN VY1472M63Y5UQ63V0
C1405: 270n 25V
C1406, C1407: 100n 25V
C1408: 1u 50V
C1409: 1n 50V
D1401, D1407, D1408, D1409: BAS16; MPN BAS16
D1402, D1403, D1405: S2M-13-F; MPN S2M-13-F
D1404: SMBJ33A; MPN SMBJ33A
D1406: BZX84-C15; MPN BZX84-C15
F1401, F1402: HP10NH1GPV160; MPN HP10NH1GPV160
F1403, F1404: 36A gPV 14x51; MPN 002637115
J1401: DC terminal + (CUSTOM)
J1402: DC terminal - (CUSTOM)
J1403: 691322110002; MPN 691322110002
J1404, J1405: 7461057; MPN 7461057
J1406: NOT FITTED - no AUX-HV tap on port 2 (D-021); MPN 7461057; not fitted
K1401: B88269X7340C011; MPN B88269X7340C011
K1402: G7L-2A-X DC24; MPN G7L-2A-X DC24
L1401: CM choke 160 A (CUSTOM)
Q1401, Q1404, Q1407: IRFL214TRPbF; MPN IRFL214TRPbF
Q1402, Q1405, Q1406, Q1409: BSS138BK; MPN BSS138BK
Q1403: IRFR9214TRPbF; MPN IRFR9214TRPbF
Q1408: C2M1000170D; MPN C2M1000170D
Q1410, Q1411: MMBT3906-7-F; MPN MMBT3906-7-F
Q1412: MMBT3904-7-F; MPN MMBT3904-7-F
R1401, R1402, R1403, R1404, R1405, R1406, R1407, R1408, R1409, R1410, R1411, R1412: 82.5k
R1413: 220k
R1414: 1.5k
R1415, R1417, R1418, R1419, R1423: 10k
R1416, R1420, R1424: 22k
R1421, R1422, R1436, R1443, R1444, R1445, R1446, R1447, R1448, R1449, R1450, R1451, R1452: 47k
R1425: 220R RST200 RFQ
R1426, R1427: 300R RST200 RFQ
R1428, R1429, R1430, R1431, R1432: TNPV12062M00BEEA; MPN TNPV12062M00BEEA
R1433, R1434, R1442: 100k
R1435: 7.32k
R1437, R1438, R1440, R1441: 1M
R1439: 4.7M
RS1401: CSM2F-8518-L100J01; MPN CSM2F-8518-L100J01
RT1401: B57703M0103A018; MPN B57703M0103A018
RV1401, RV1402, RV1403: TVT25751KFKG; MPN TVT25751KFKG
RV1404: B72210S0300K101; MPN B72210S0300K101
S1401: KSD301 NO 80C RFQ
U1401: CNY65B; MPN CNY65B
U1402: TPSI3050QDWZRQ1; MPN TPSI3050QDWZRQ1
X1401, X1402, X1403, X1404: 006710340; MPN 006710340

Connections:
+3V3S: R1413.1
+24V: Q1403.3 (S), R1414.1, R1418.1
AGND: U1401.3 (E)
B_BL1: R1443.2, R1444.1
B_BL2: R1444.2, R1445.1
B_BL3: R1445.2, R1446.1
B_BL4: R1446.2, R1447.1
B_BL5: R1447.2, R1448.1
B_BL6: R1448.2, R1449.1
B_BL7: R1449.2, R1450.1
B_BL8: R1450.2, R1451.1
B_BL9: R1451.2, R1452.1
B_DIS_B1: R1428.2, R1429.1
B_DIS_B2: R1429.2, R1430.1
B_DIS_B3: R1430.2, R1431.1
B_DIS_B4: R1431.2, R1432.1
B_DIS_D: Q1408.2 (D), R1427.2
B_DIS_EN: D1407.3 (K), D1408.3 (K), R1434.1, U1402.1 (EN)
B_DIS_G: D1406.3 (K), Q1408.1 (G), Q1409.3 (D), Q1411.2 (E), R1432.2, R1437.1, R1439.1, R1440.1, S1401.1 (A)
B_DIS_M: R1426.2, R1427.1
B_DIS_OFF: Q1409.1 (G), R1433.1, U1402.8 (VDRV)
B_DIS_PX: R1435.1, U1402.2 (PXFR)
B_DIS_REF: Q1410.1 (B), R1437.2, R1438.1
B_DIS_SB: Q1411.1 (B), Q1412.3 (C), R1440.2
B_DIS_SG: C1409.1, Q1410.3 (C), Q1411.3 (C), Q1412.1 (B), R1441.1, R1442.2
B_DIS_T: C1408.1, D1409.1 (A), R1439.2
B_DIS_TE: D1409.3 (K), Q1410.2 (E)
B_DIS_TH: R1442.1, S1401.2 (B)
B_DIS_VDDH: C1406.1, U1402.7 (VDDH)
B_DIS_VDDM: C1406.2, C1407.1, U1402.6 (VDDM)
B_DIS_VDDP: C1405.1, U1402.3 (VDDP)
B_F+: C1401.1, F1401.2, L1401.1 (A1)
B_F-: C1401.2, F1402.2, L1401.3 (B1)
B_HC1_HOLD: Q1402.1 (G)
B_HC2_HOLD: Q1406.1 (G)
B_HC_G2: Q1404.1 (G), Q1405.3 (D), R1419.2, R1420.1
B_HC_OUT: D1403.2 (A), Q1403.2 (D), R1419.1, R1421.1
B_HC_PD: Q1402.3 (D), R1417.1
B_HC_PG: Q1403.1 (G), R1417.2, R1418.2
B_HC_X: Q1405.1 (G), Q1406.3 (D), R1421.2, R1422.1
B_IN+: F1401.1, F1403.1, J1401.1, X1401.1
B_IN-: F1402.1, F1404.1, J1402.1, X1403.1
B_KM_COIL: D1402.1 (K), D1403.1 (K), K1401.2 (COIL+), RV1404.1
B_KM_G1: Q1401.1 (G), R1415.2, R1416.1
B_KM_LO: K1401.3 (COIL-), Q1401.2 (D), Q1404.2 (D), RV1404.2
B_KP_G: Q1407.1 (G), R1423.2, R1424.1
B_KP_LO: D1404.1 (K), K1402.0 (COIL), Q1407.2 (D)
B_KP_Z: D1404.2 (A), D1405.2 (A)
B_MON1: R1401.1, RV1401.3 (MON)
B_MON2: R1412.2, RV1402.3 (MON)
B_MON3: D1401.1 (A), RV1403.3 (MON), U1401.2 (K)
B_MONA: D1401.3 (K), R1406.2, U1401.1 (A)
B_MR1: R1401.2, R1402.1
B_MR2: R1402.2, R1403.1
B_MR3: R1403.2, R1404.1
B_MR4: R1404.2, R1405.1
B_MR5: R1405.2, R1406.1
B_MS1: R1407.2, R1408.1
B_MS2: R1408.2, R1409.1
B_MS3: R1409.2, R1410.1
B_MS4: R1410.2, R1411.1
B_MS5: R1411.2, R1412.1
B_PRE_M: K1402.4 (P2), K1402.6 (P1)
B_PRE_R: K1402.2 (P2-), R1425.1
B_SH_N: RS1401.3 (SENSE1)
B_SH_P: RS1401.4 (SENSE2)
B_SP+: F1403.2, RV1401.1 (L), X1402.1
B_SP-: F1404.2, RV1402.1 (L), X1404.1
B_SPD_N: R1413.2, U1401.4 (C)
B_SPM: R1407.1, RV1401.2 (N), RV1402.2 (N), RV1403.1 (L)
B_X+: C1402.1, C1403.1, J1406.1, K1401.A1, K1402.8 (P1+), L1401.2 (A2)
B_X-: C1402.2, C1404.1, L1401.4 (B2), RS1401.1 (BOLT1)
FB_B_MAIN: D1408.1 (A), K1401.4 (AUX_NC), R1414.2
GND: C1405.2, K1401.1 (AUX_COM), Q1401.3 (S), Q1402.2 (S), Q1404.3 (S), Q1405.2 (S), Q1406.2 (S), Q1407.3 (S), R1416.2, R1420.2, R1422.2, R1424.2, R1434.2, R1435.2, R1436.2, U1402.4 (VSSP)
K_B_MAIN: D1402.2 (A), R1415.1
K_B_PRE: D1405.1 (K), K1402.1 (COIL), R1423.1
K_DISCH: D1407.1 (A), R1436.1
NTC_B_1: J1403.1, RT1401.1
NTC_B_2: J1403.2, RT1401.2
P2_BUS+: J1404.1, K1401.A2, R1425.2, R1426.1, R1428.1, R1443.1
P2_BUS-: C1407.2, C1408.2, C1409.2, D1406.1 (A), J1405.1, Q1408.3 (S), Q1409.2 (S), Q1412.2 (E), R1433.2, R1438.2, R1441.2, R1452.2, RS1401.2 (BOLT2), U1402.5 (VSSS)
PE: C1403.2, C1404.2, RV1403.2 (N)

Notes on the sheet:
G7L-2A-X, poles in series, normal polarity = current 8 -> 2 (terminal -> bus). K_B_PRE feeds the coil and gates its IRFL214 low side; S2M + SMBJ33A across the coil (37-42 V, Omron p5). R_pre 220 ohm Miba RST 200 (RFQ, pulse-rated). Complete at |dV| <= 10 V after the VA/VAX null; abort below 0.8 x V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
MAIN CONTACTOR: COIL DRIVE + FEEDBACK
PASSIVE BLEEDER + BOARD CONNECTION POINTS
DISCHARGE TIME LIMIT + THERMAL CUT-OFF (HV SIDE, NEEDS NO 24 V)
10 x 47 k 2512 1 W (100 V each at 1000 V): back-up discharge, 2.4 W at 1000 V. REDCUBE studs: bus +/- to the power cells, terminal-side tap.
TPSI3050 EN = K_DISCH OR FB_B_MAIN (2 x BAS16): powered = BSS138 holds the SiC gate low. Unpowered = the bus biases the gate (10 M, 15 V zener) -> 2 x 300 ohm Miba RST 200 discharge the bus. FB is high while the contactor is closed (or welded), so an E-stop or a lost K_DISCH cannot discharge a live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
CHASSIS-MOUNTED. 135 A port: gPV 160 A 1000 V DC in each pole, derated 124 A (fuses in the INLET air path, PD3: terminals / fuse bases only, creepage to PE >= 16.0 mm IIIa, IC-18/IC-21).
FAIL-SAFE ACTIVE DISCHARGE, INHIBITED WHILE THE CONTACTOR IS CLOSED
HVC43-250A-24MC, + pole, bidirectional (TDK p2). Opens at zero current in normal operation; cut-off 450 A @ 1000 V once. K_B_MAIN feeds coil+ (S2M) AND gates the IRFL214 low side: two switches in the path. S10K30 directly across the coil = the only flyback path (>= 54 V down to drop-out; TDK p7 >= 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
Channel 1: HOLD1 -> BSS138 -> IRFR9214 high side from the port +24V (not cut by E-stop) -> S2M -> coil+. Channel 2: IRFL214 low side coil- -> GND, gate fed from the channel-1 output (10 k / 22 k) and clamped off by a BSS138 unless HOLD2: it can only conduct while channel 1 conducts, so no flyback e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
EMI FILTER
ON-BOARD SURGE PROTECTION: VARISTOR Y (IC-01, IC-12)
SHUNT (- POLE) + SHUNT NTC
DIS_G charges 1 uF through 4.7 M; a MMBT3906 compares it with DIS_G/2 (1 M / 1 M, also the gate pull- down) and fires the MMBT3906/MMBT3904 latch: gate clamped to 0.75 V after 2.4-5.1 s (needed <= 1.8 s), held by the bias current until K_DISCH returns (BSS138 resets it). Thermostat KSD301-class (cl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
PRECHARGE RELAY + RESISTOR
HOLD-CLOSED POWER STAGE (2 INDEPENDENT CHANNELS)
X 2 x 2.2 uF film (RFQ: impulse >= 4.5 kV, PA-07), CM choke (CUSTOM), Y1 4.7 nF pole-PE (1500 VDC rated). Y capacitors are declared HV-PE crossings.
TVT25751 x 3 (615 VDC, thermal link + monitor lead): MOV1 +/M, MOV2 -/M, MOV3 M/PE_T. Up,eff 3793 V pole-PE and pole-pole at In 3 kA (calc., <= 4.0 kV -> reinforced 6 kV / basic 4 kV, D-032); Imax 25 kA. Branch fuses ETI CH14x51 gPV 36 A 30 kA (L/R 2 ms). Monitor loop through both fuses and all thr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
TERMINALS, FUSES (PV-TYPE PORT)
CSM2F-8518 100 uOhm, busbar-mounted. Kelvin test points to the IA/IB amplifier. Positive current = power into the module at this port. NTC on the shunt (reinforced pad) -> SYS-IO-AUX NTC input: firmware TCR compensation.
