vectivolt/PCM/hardware/DAB60/sheets/15_portB_sense.kicad_sch

## KiCad design hardware/DAB60/sheets/15_portB_sense.kicad_sch (2026-10-04)

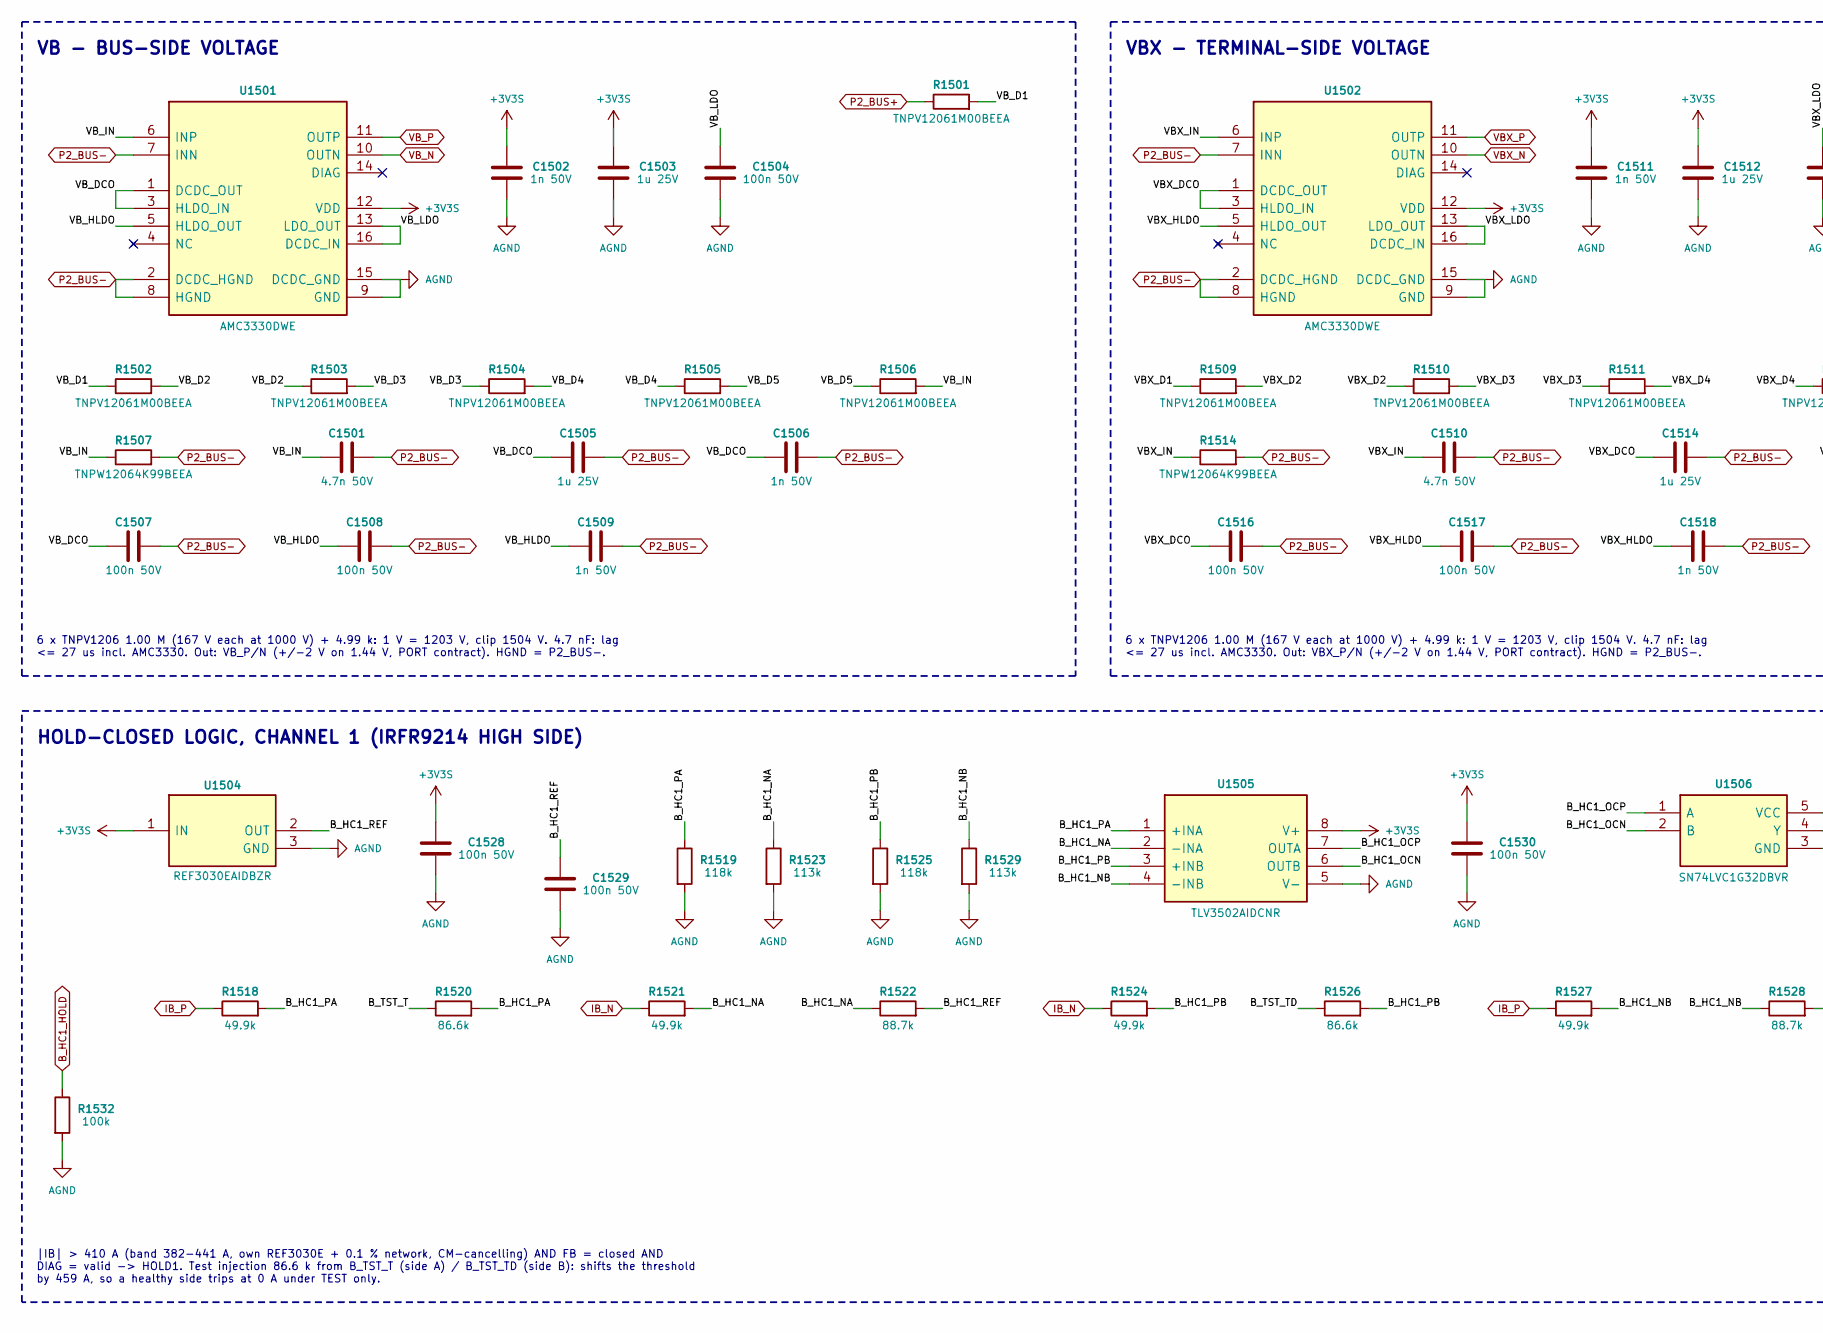
[picture p261: schematic 15_portB_sense.kicad_sch, part in row 1, column 1]

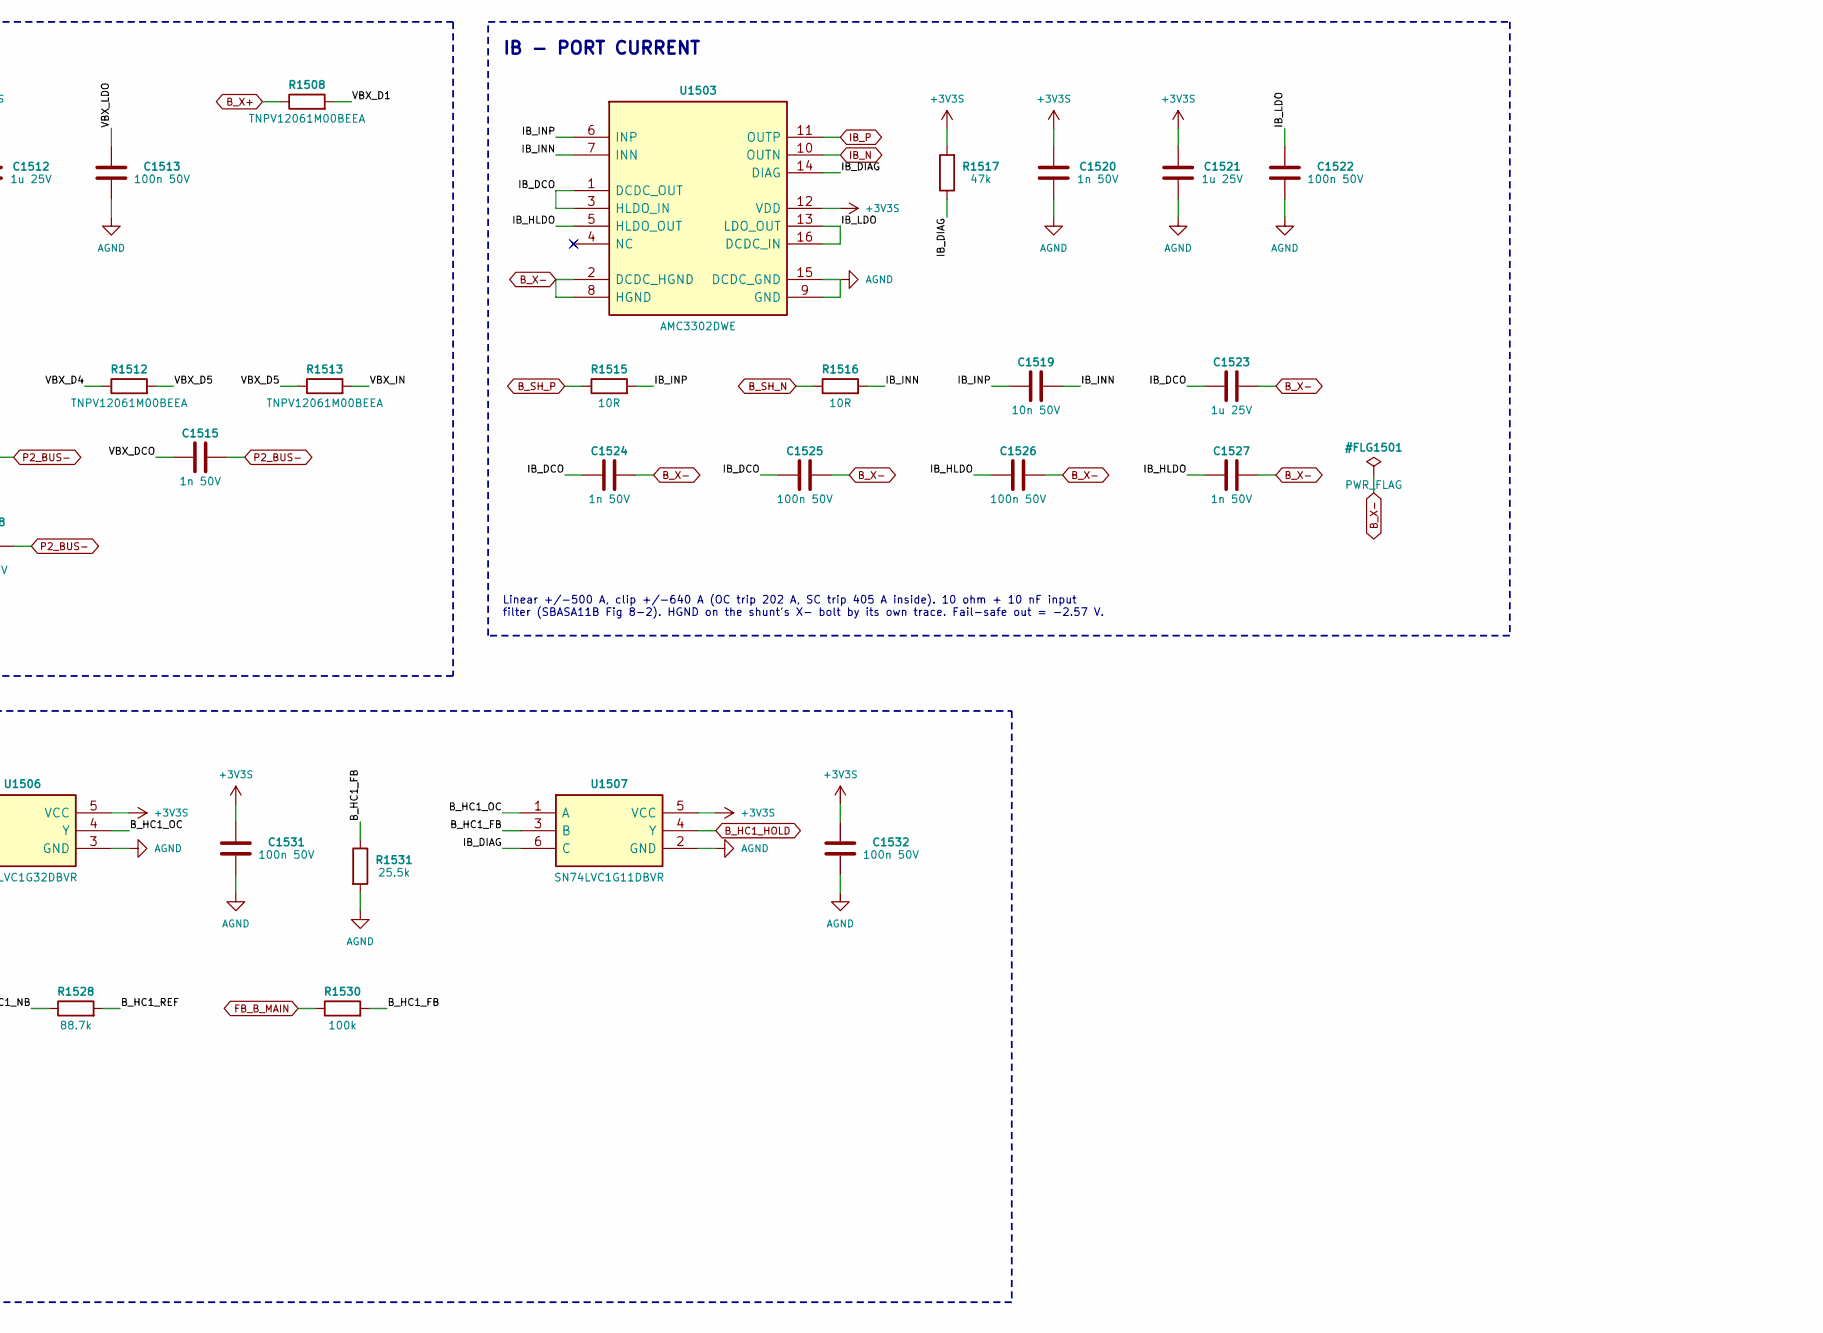
[picture p262: schematic 15_portB_sense.kicad_sch, part in row 1, column 2]

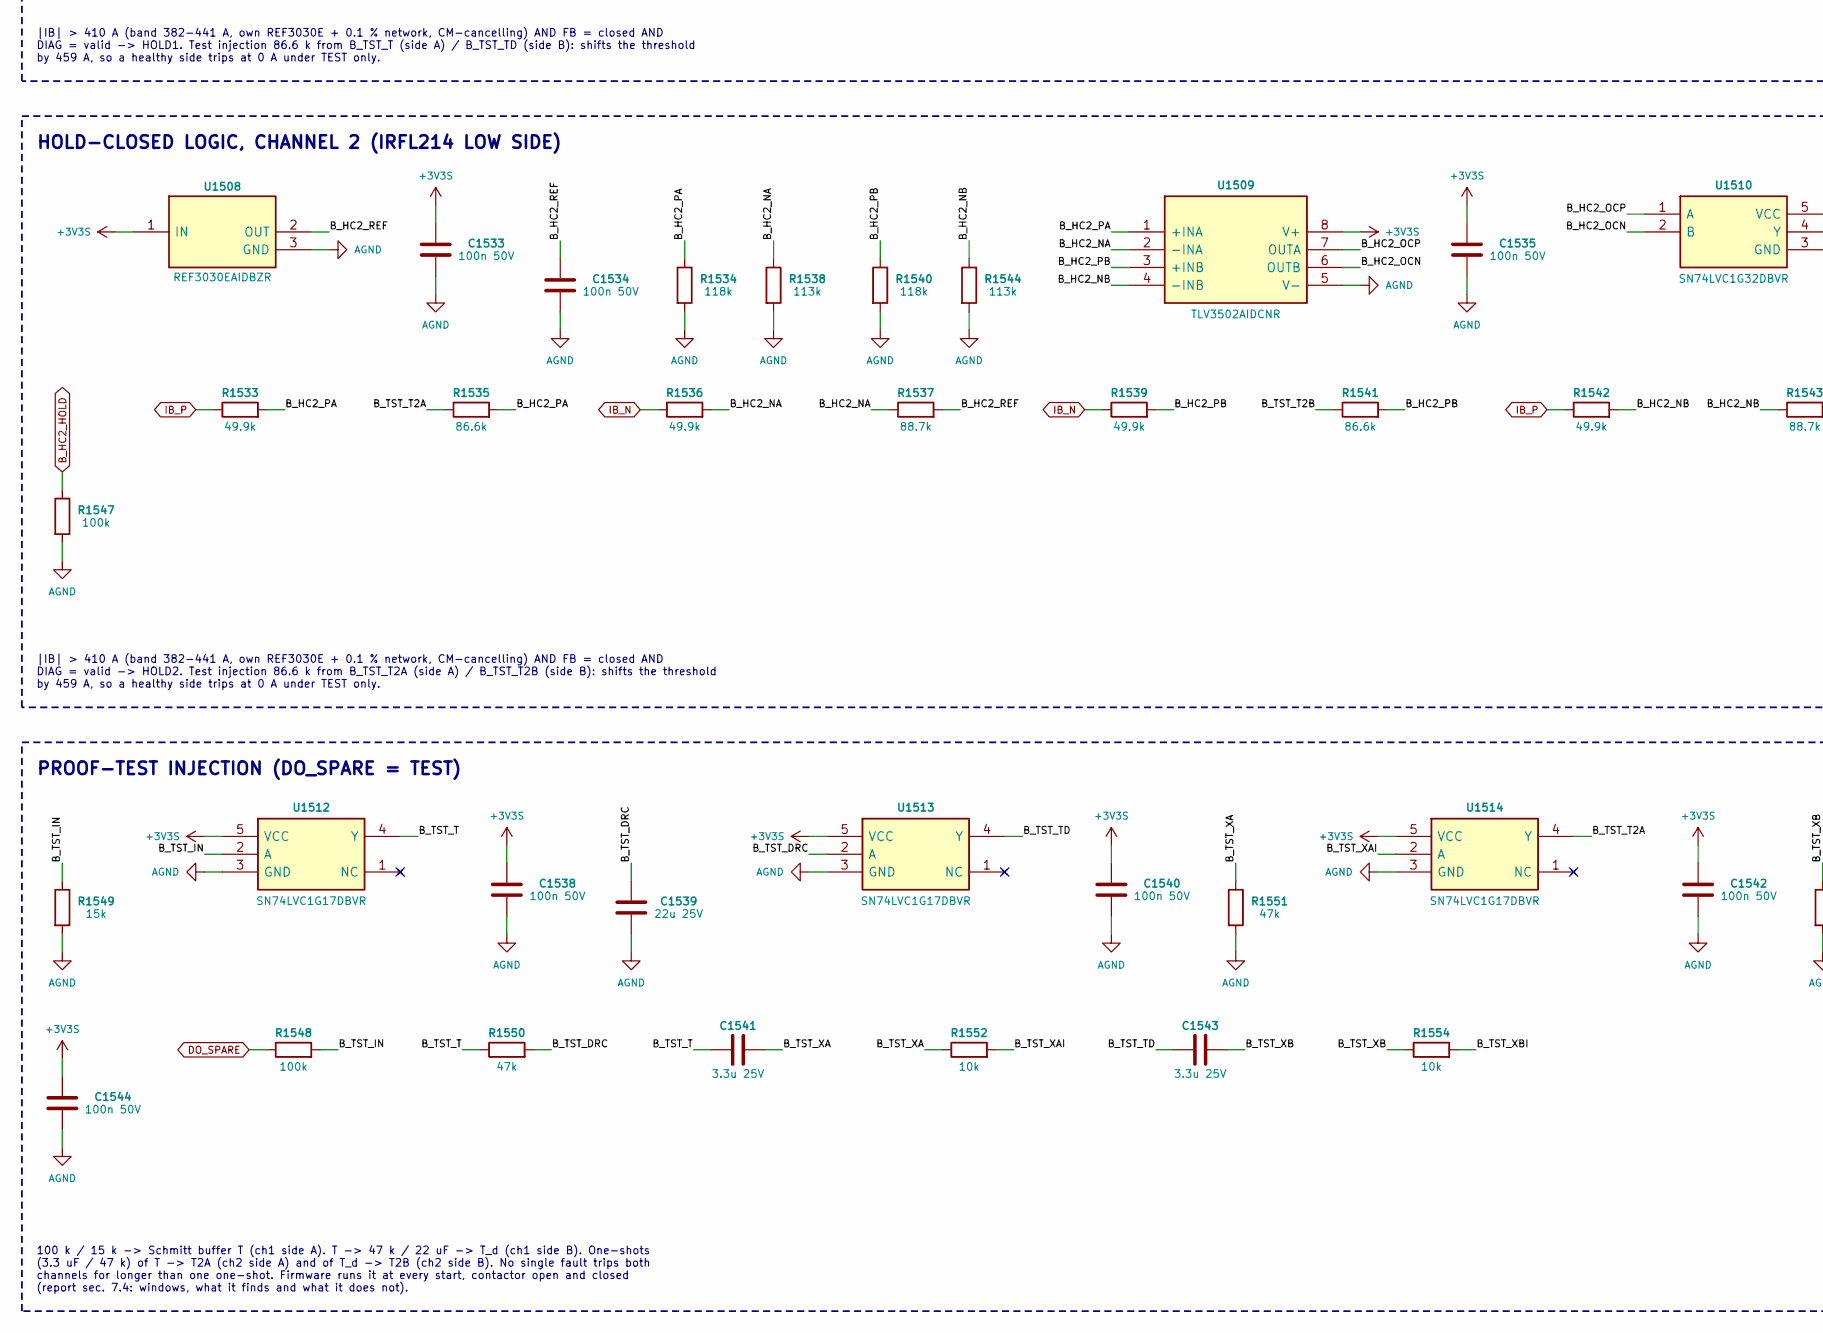
[picture p263: schematic 15_portB_sense.kicad_sch, part in row 2, column 1]

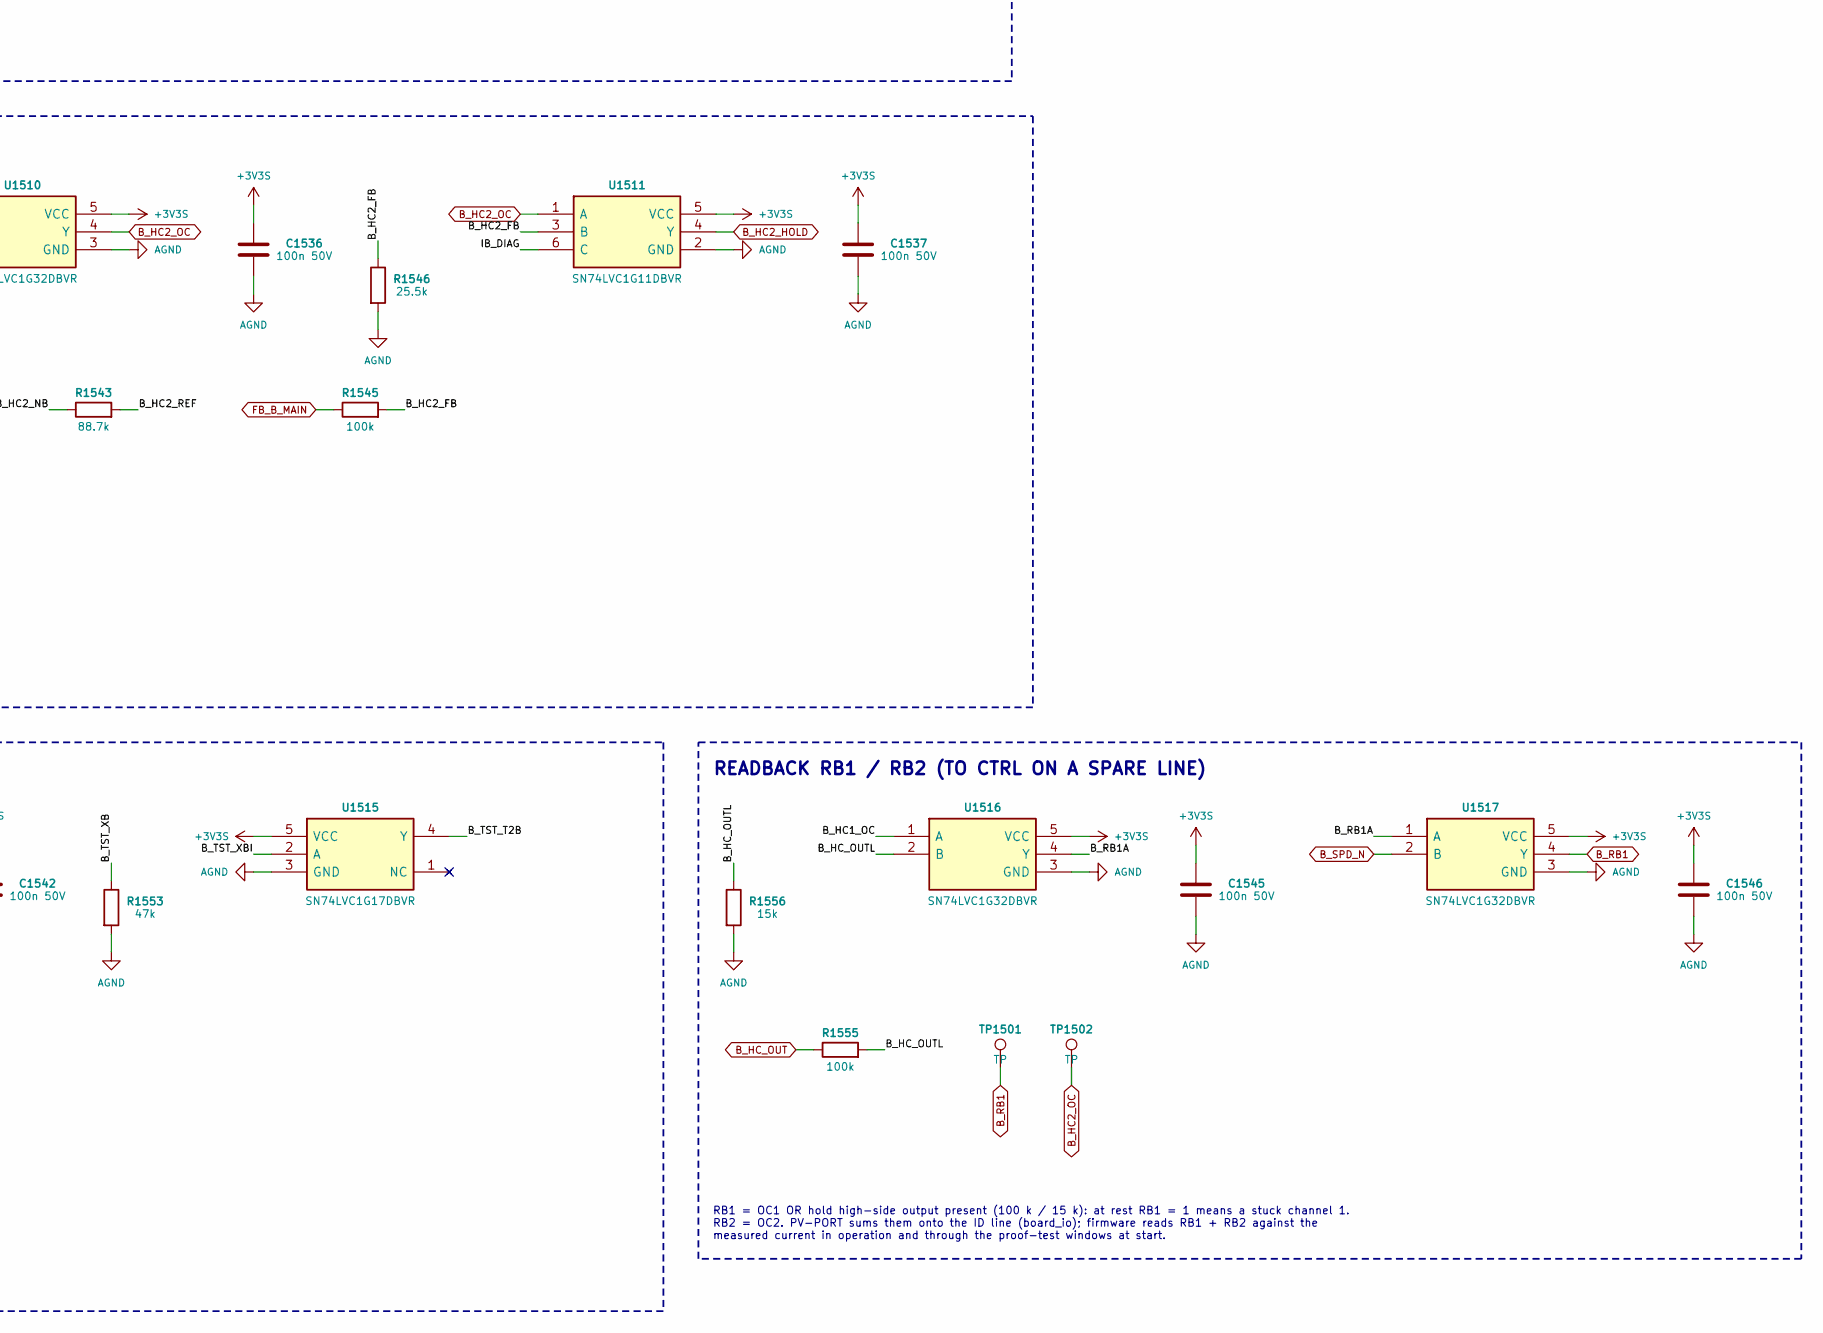
[picture p264: schematic 15_portB_sense.kicad_sch, part in row 2, column 2]

Parts:
C1501, C1510: 4.7n 50V
C1502, C1506, C1509, C1511, C1515, C1518, C1520, C1524, C1527: 1n 50V
C1503, C1505, C1512, C1514, C1521, C1523: 1u 25V
C1504, C1507, C1508, C1513, C1516, C1517, C1522, C1525, C1526, C1528, C1529, C1530, C1531, C1532, C1533, C1534, C1535, C1536, C1537, C1538, C1540, C1542, C1544, C1545, C1546: 100n 50V
C1519: 10n 50V
C1539: 22u 25V
C1541, C1543: 3.3u 25V
R1501, R1502, R1503, R1504, R1505, R1506, R1508, R1509, R1510, R1511, R1512, R1513: TNPV12061M00BEEA; MPN TNPV12061M00BEEA
R1507, R1514: TNPW12064K99BEEA; MPN TNPW12064K99BEEA
R1515, R1516: 10R
R1517, R1550, R1551, R1553: 47k
R1518, R1521, R1524, R1527, R1533, R1536, R1539, R1542: 49.9k
R1519, R1525, R1534, R1540: 118k
R1520, R1526, R1535, R1541: 86.6k
R1522, R1528, R1537, R1543: 88.7k
R1523, R1529, R1538, R1544: 113k
R1530, R1532, R1545, R1547, R1548, R1555: 100k
R1531, R1546: 25.5k
R1549, R1556: 15k
R1552, R1554: 10k
TP1501, TP1502: TP
U1501, U1502: AMC3330DWE; MPN AMC3330DWE
U1503: AMC3302DWE; MPN AMC3302DWE
U1504, U1508: REF3030EAIDBZR; MPN REF3030EAIDBZR
U1505, U1509: TLV3502AIDCNR; MPN TLV3502AIDCNR
U1506, U1510, U1516, U1517: SN74LVC1G32DBVR; MPN SN74LVC1G32DBVR
U1507, U1511: SN74LVC1G11DBVR; MPN SN74LVC1G11DBVR
U1512, U1513, U1514, U1515: SN74LVC1G17DBVR; MPN SN74LVC1G17DBVR

Connections:
+3V3S: C1502.1, C1503.1, C1511.1, C1512.1, C1520.1, C1521.1, C1528.1, C1530.1, C1531.1, C1532.1, C1533.1, C1535.1, C1536.1, C1537.1, C1538.1, C1540.1, C1542.1, C1544.1, C1545.1, C1546.1, R1517.2, U1501.12 (VDD), U1502.12 (VDD), U1503.12 (VDD), U1504.1 (IN), U1505.8 (V+), U1506.5 (VCC), U1507.5 (VCC), U1508.1 (IN), U1509.8 (V+), U1510.5 (VCC), U1511.5 (VCC), U1512.5 (VCC), U1513.5 (VCC), U1514.5 (VCC), U1515.5 (VCC), U1516.5 (VCC), U1517.5 (VCC)
AGND: C1502.2, C1503.2, C1504.2, C1511.2, C1512.2, C1513.2, C1520.2, C1521.2, C1522.2, C1528.2, C1529.2, C1530.2, C1531.2, C1532.2, C1533.2, C1534.2, C1535.2, C1536.2, C1537.2, C1538.2, C1539.2, C1540.2, C1542.2, C1544.2, C1545.2, C1546.2, R1519.2, R1523.2, R1525.2, R1529.2, R1531.2, R1532.2, R1534.2, R1538.2, R1540.2, R1544.2, R1546.2, R1547.2, R1549.2, R1551.2, R1553.2, R1556.2, U1501.9 (GND), U1501.15 (DCDC_GND), U1502.9 (GND), U1502.15 (DCDC_GND), U1503.9 (GND), U1503.15 (DCDC_GND), U1504.3 (GND), U1505.5 (V-), U1506.3 (GND), U1507.2 (GND), U1508.3 (GND), U1509.5 (V-), U1510.3 (GND), U1511.2 (GND), U1512.3 (GND), U1513.3 (GND), U1514.3 (GND), U1515.3 (GND), U1516.3 (GND), U1517.3 (GND)
B_HC1_FB: R1530.2, R1531.1, U1507.3 (B)
B_HC1_HOLD: R1532.1, U1507.4 (Y)
B_HC1_NA: R1521.2, R1522.1, R1523.1, U1505.2 (-INA)
B_HC1_NB: R1527.2, R1528.1, R1529.1, U1505.4 (-INB)
B_HC1_OC: U1506.4 (Y), U1507.1 (A), U1516.1 (A)
B_HC1_OCN: U1505.6 (OUTB), U1506.2 (B)
B_HC1_OCP: U1505.7 (OUTA), U1506.1 (A)
B_HC1_PA: R1518.2, R1519.1, R1520.2, U1505.1 (+INA)
B_HC1_PB: R1524.2, R1525.1, R1526.2, U1505.3 (+INB)
B_HC1_REF: C1529.1, R1522.2, R1528.2, U1504.2 (OUT)
B_HC2_FB: R1545.2, R1546.1, U1511.3 (B)
B_HC2_HOLD: R1547.1, U1511.4 (Y)
B_HC2_NA: R1536.2, R1537.1, R1538.1, U1509.2 (-INA)
B_HC2_NB: R1542.2, R1543.1, R1544.1, U1509.4 (-INB)
B_HC2_OC: TP1502.1, U1510.4 (Y), U1511.1 (A)
B_HC2_OCN: U1509.6 (OUTB), U1510.2 (B)
B_HC2_OCP: U1509.7 (OUTA), U1510.1 (A)
B_HC2_PA: R1533.2, R1534.1, R1535.2, U1509.1 (+INA)
B_HC2_PB: R1539.2, R1540.1, R1541.2, U1509.3 (+INB)
B_HC2_REF: C1534.1, R1537.2, R1543.2, U1508.2 (OUT)
B_HC_OUT: R1555.1
B_HC_OUTL: R1555.2, R1556.1, U1516.2 (B)
B_RB1: TP1501.1, U1517.4 (Y)
B_RB1A: U1516.4 (Y), U1517.1 (A)
B_SH_N: R1516.1
B_SH_P: R1515.1
B_SPD_N: U1517.2 (B)
B_TST_DRC: C1539.1, R1550.2, U1513.2 (A)
B_TST_IN: R1548.2, R1549.1, U1512.2 (A)
B_TST_T: C1541.1, R1520.1, R1550.1, U1512.4 (Y)
B_TST_T2A: R1535.1, U1514.4 (Y)
B_TST_T2B: R1541.1, U1515.4 (Y)
B_TST_TD: C1543.1, R1526.1, U1513.4 (Y)
B_TST_XA: C1541.2, R1551.1, R1552.1
B_TST_XAI: R1552.2, U1514.2 (A)
B_TST_XB: C1543.2, R1553.1, R1554.1
B_TST_XBI: R1554.2, U1515.2 (A)
B_X+: R1508.1
B_X-: C1523.2, C1524.2, C1525.2, C1526.2, C1527.2, U1503.2 (DCDC_HGND), U1503.8 (HGND)
DO_SPARE: R1548.1
FB_B_MAIN: R1530.1, R1545.1
IB_DCO: C1523.1, C1524.1, C1525.1, U1503.1 (DCDC_OUT), U1503.3 (HLDO_IN)
IB_DIAG: R1517.1, U1503.14 (DIAG), U1507.6 (C), U1511.6 (C)
IB_HLDO: C1526.1, C1527.1, U1503.5 (HLDO_OUT)
IB_INN: C1519.2, R1516.2, U1503.7 (INN)
IB_INP: C1519.1, R1515.2, U1503.6 (INP)
IB_LDO: C1522.1, U1503.13 (LDO_OUT), U1503.16 (DCDC_IN)
IB_N: R1521.1, R1524.1, R1536.1, R1539.1, U1503.10 (OUTN)
IB_P: R1518.1, R1527.1, R1533.1, R1542.1, U1503.11 (OUTP)
P2_BUS+: R1501.1
P2_BUS-: C1501.2, C1505.2, C1506.2, C1507.2, C1508.2, C1509.2, C1510.2, C1514.2, C1515.2, C1516.2, C1517.2, C1518.2, R1507.2, R1514.2, U1501.2 (DCDC_HGND), U1501.7 (INN), U1501.8 (HGND), U1502.2 (DCDC_HGND), U1502.7 (INN), U1502.8 (HGND)
VBX_D1: R1508.2, R1509.1
VBX_D2: R1509.2, R1510.1
VBX_D3: R1510.2, R1511.1
VBX_D4: R1511.2, R1512.1
VBX_D5: R1512.2, R1513.1
VBX_DCO: C1514.1, C1515.1, C1516.1, U1502.1 (DCDC_OUT), U1502.3 (HLDO_IN)
VBX_HLDO: C1517.1, C1518.1, U1502.5 (HLDO_OUT)
VBX_IN: C1510.1, R1513.2, R1514.1, U1502.6 (INP)
VBX_LDO: C1513.1, U1502.13 (LDO_OUT), U1502.16 (DCDC_IN)
VBX_N: U1502.10 (OUTN)
VBX_P: U1502.11 (OUTP)
VB_D1: R1501.2, R1502.1
VB_D2: R1502.2, R1503.1
VB_D3: R1503.2, R1504.1
VB_D4: R1504.2, R1505.1
VB_D5: R1505.2, R1506.1
VB_DCO: C1505.1, C1506.1, C1507.1, U1501.1 (DCDC_OUT), U1501.3 (HLDO_IN)
VB_HLDO: C1508.1, C1509.1, U1501.5 (HLDO_OUT)
VB_IN: C1501.1, R1506.2, R1507.1, U1501.6 (INP)
VB_LDO: C1504.1, U1501.13 (LDO_OUT), U1501.16 (DCDC_IN)
VB_N: U1501.10 (OUTN)
VB_P: U1501.11 (OUTP)

Notes on the sheet:
|IB| > 410 A (band 382-441 A, own REF3030E + 0.1 % network, CM-cancelling) AND FB = closed AND DIAG = valid -> HOLD1. Test injection 86.6 k from B_TST_T (side A) / B_TST_TD (side B): shifts the threshold by 459 A, so a healthy side trips at 0 A under TEST only.
VB - BUS-SIDE VOLTAGE
HOLD-CLOSED LOGIC, CHANNEL 2 (IRFL214 LOW SIDE)
Linear +/-500 A, clip +/-640 A (OC trip 202 A, SC trip 405 A inside). 10 ohm + 10 nF input filter (SBASA11B Fig 8-2). HGND on the shunt's X- bolt by its own trace. Fail-safe out = -2.57 V.
6 x TNPV1206 1.00 M (167 V each at 1000 V) + 4.99 k: 1 V = 1203 V, clip 1504 V. 4.7 nF: lag <= 27 us incl. AMC3330. Out: VB_P/N (+/-2 V on 1.44 V, PORT contract). HGND = P2_BUS-.
IB - PORT CURRENT
READBACK RB1 / RB2 (TO CTRL ON A SPARE LINE)
RB1 = OC1 OR hold high-side output present (100 k / 15 k): at rest RB1 = 1 means a stuck channel 1. RB2 = OC2. PV-PORT sums them onto the ID line (board_io); firmware reads RB1 + RB2 against the measured current in operation and through the proof-test windows at start.
|IB| > 410 A (band 382-441 A, own REF3030E + 0.1 % network, CM-cancelling) AND FB = closed AND DIAG = valid -> HOLD2. Test injection 86.6 k from B_TST_T2A (side A) / B_TST_T2B (side B): shifts the threshold by 459 A, so a healthy side trips at 0 A under TEST only.
100 k / 15 k -> Schmitt buffer T (ch1 side A). T -> 47 k / 22 uF -> T_d (ch1 side B). One-shots (3.3 uF / 47 k) of T -> T2A (ch2 side A) and of T_d -> T2B (ch2 side B). No single fault trips both channels for longer than one one-shot. Firmware runs it at every start, contactor open and closed (repo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
HOLD-CLOSED LOGIC, CHANNEL 1 (IRFR9214 HIGH SIDE)
PROOF-TEST INJECTION (DO_SPARE = TEST)
VBX - TERMINAL-SIDE VOLTAGE
6 x TNPV1206 1.00 M (167 V each at 1000 V) + 4.99 k: 1 V = 1203 V, clip 1504 V. 4.7 nF: lag <= 27 us incl. AMC3330. Out: VBX_P/N (+/-2 V on 1.44 V, PORT contract). HGND = P2_BUS-.
