vectivolt/PCM/hardware/DAB60/sheets/16_io.kicad_sch

## KiCad design hardware/DAB60/sheets/16_io.kicad_sch (2026-10-04)

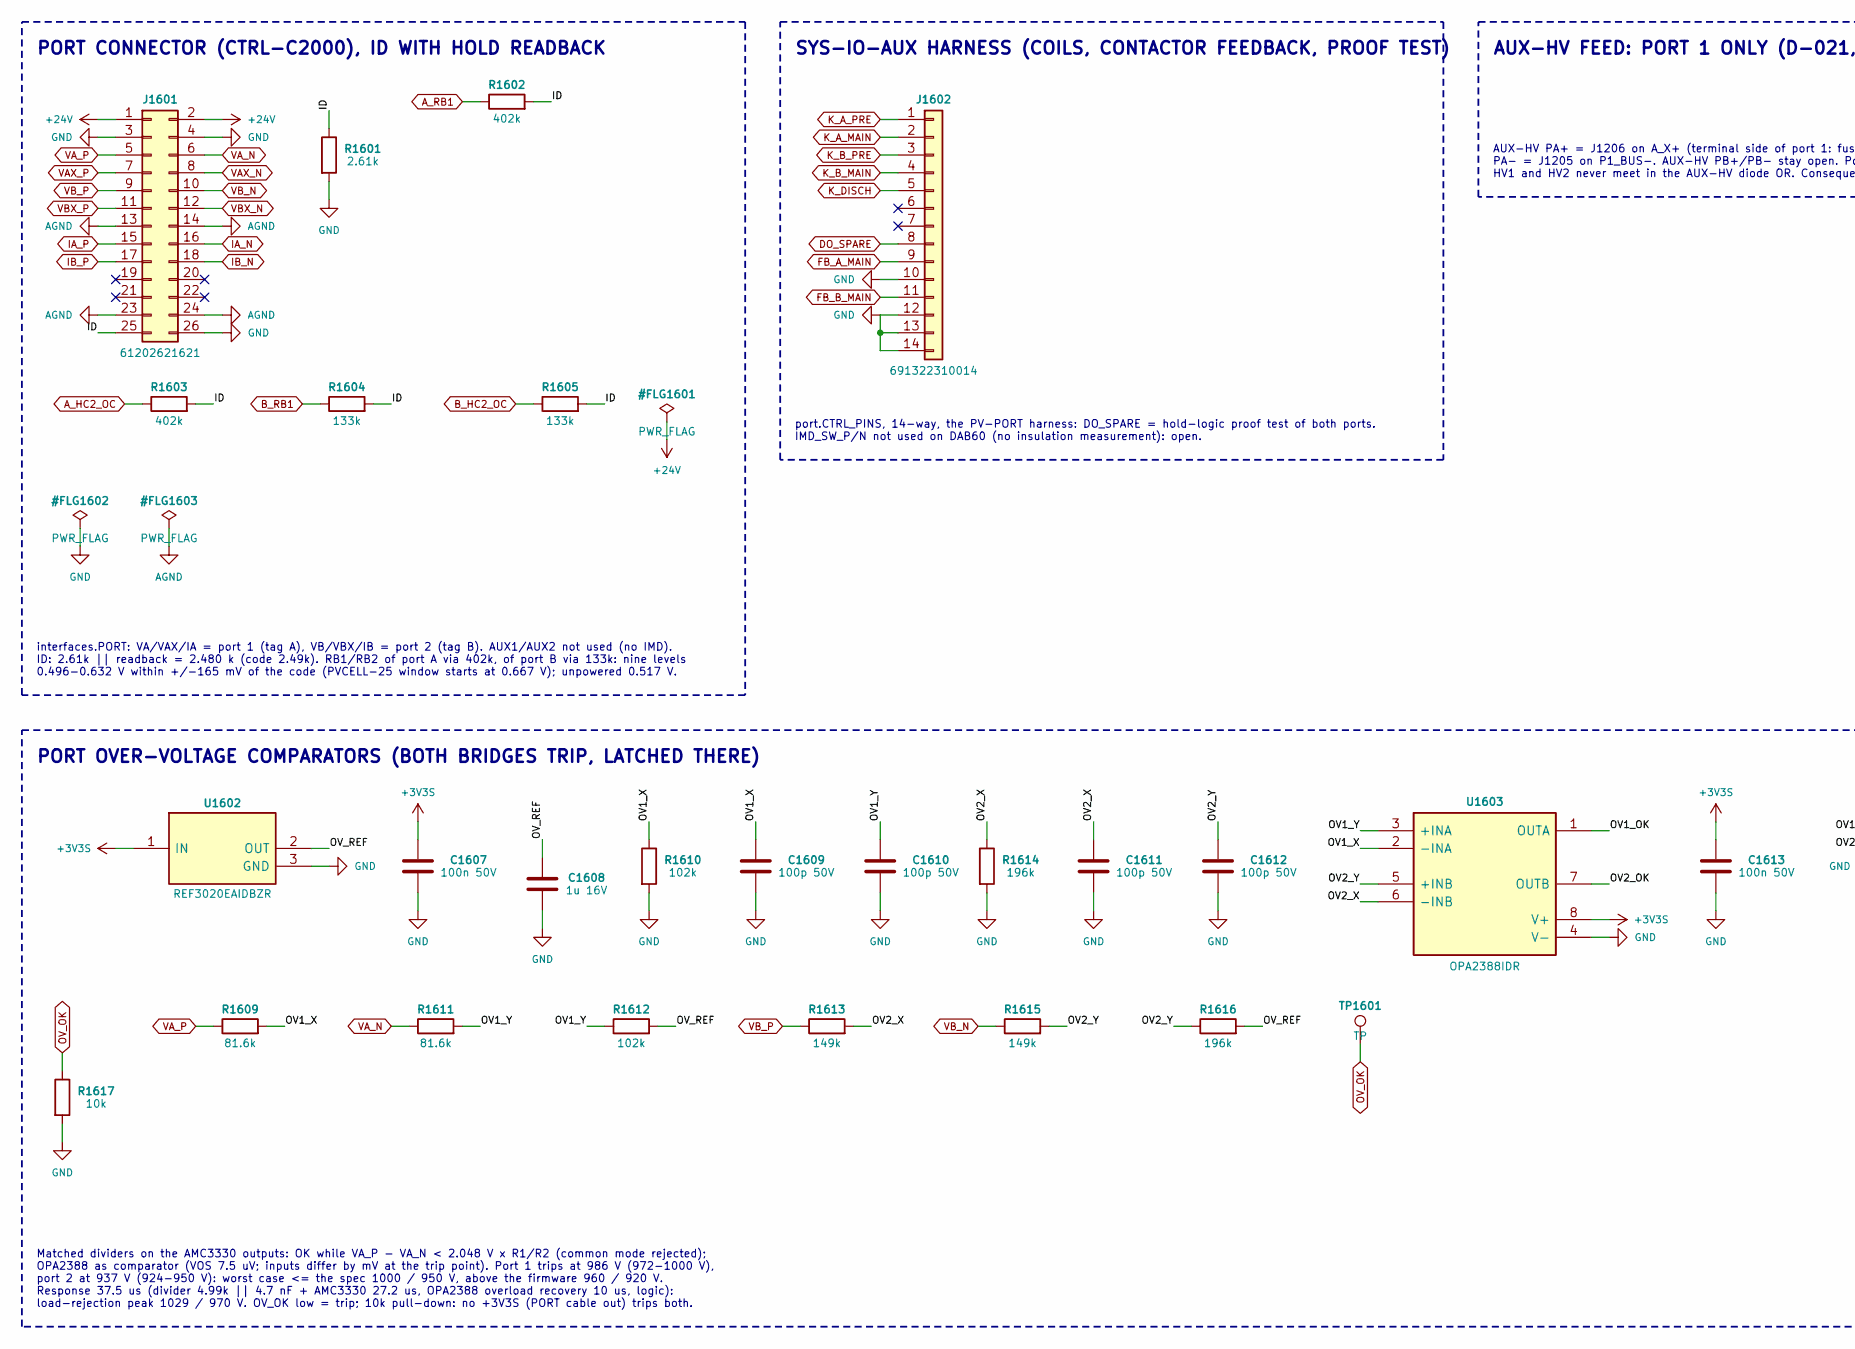
[picture p265: schematic 16_io.kicad_sch, part in row 1, column 1]

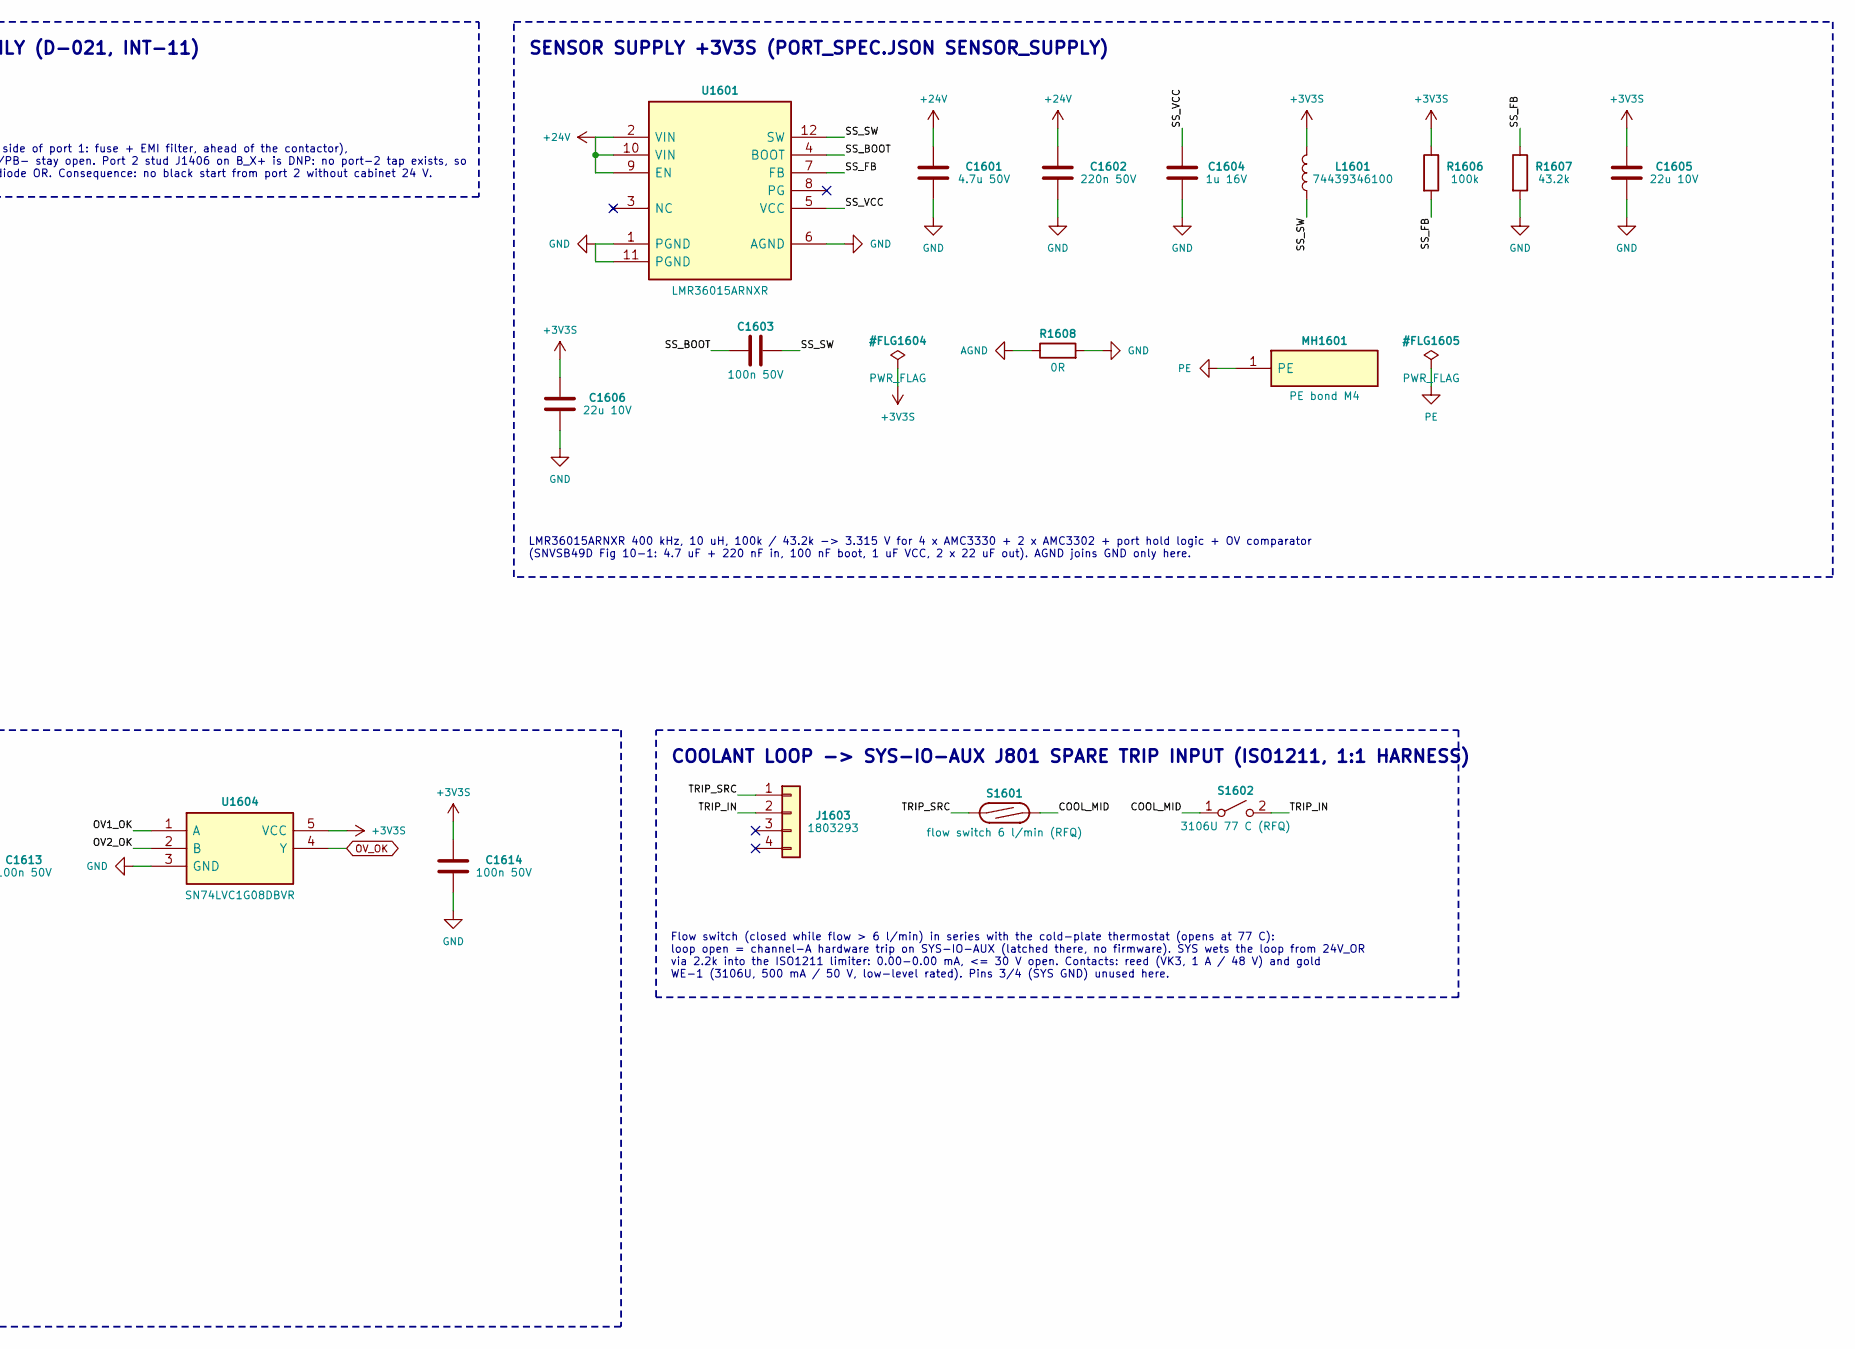
[picture p266: schematic 16_io.kicad_sch, part in row 1, column 2]

Parts:
C1601: 4.7u 50V
C1602: 220n 50V
C1603, C1607, C1613, C1614: 100n 50V
C1604, C1608: 1u 16V
C1605, C1606: 22u 10V
C1609, C1610, C1611, C1612: 100p 50V
J1601: 61202621621; MPN 61202621621
J1602: 691322310014; MPN 691322310014
J1603: 1803293; MPN 1803293
L1601: 74439346100; MPN 74439346100
MH1601: PE bond M4
R1601: 2.61k
R1602, R1603: 402k
R1604, R1605: 133k
R1606: 100k
R1607: 43.2k
R1608: 0R
R1609, R1611: 81.6k
R1610, R1612: 102k
R1613, R1615: 149k
R1614, R1616: 196k
R1617: 10k
S1601: flow switch 6 l/min (RFQ); MPN VK315M0P10PI31
S1602: 3106U 77 C (RFQ); MPN 3106U
TP1601: TP
U1601: LMR36015ARNXR; MPN LMR36015ARNXR
U1602: REF3020EAIDBZR; MPN REF3020EAIDBZR
U1603: OPA2388IDR; MPN OPA2388IDR
U1604: SN74LVC1G08DBVR; MPN SN74LVC1G08DBVR

Connections:
+3V3S: C1605.1, C1606.1, C1607.1, C1613.1, C1614.1, L1601.2, R1606.1, U1602.1 (IN), U1603.8 (V+), U1604.5 (VCC)
+24V: C1601.1, C1602.1, J1601.1, J1601.2, U1601.2 (VIN), U1601.9 (EN), U1601.10 (VIN)
AGND: J1601.13, J1601.14, J1601.23, J1601.24, R1608.1
A_HC2_OC: R1603.1
A_RB1: R1602.1
B_HC2_OC: R1605.1
B_RB1: R1604.1
COOL_MID: S1601.2, S1602.1 (A)
DO_SPARE: J1602.8
FB_A_MAIN: J1602.9
FB_B_MAIN: J1602.11
GND: C1601.2, C1602.2, C1604.2, C1605.2, C1606.2, C1607.2, C1608.2, C1609.2, C1610.2, C1611.2, C1612.2, C1613.2, C1614.2, J1601.3, J1601.4, J1601.26, J1602.10, J1602.12, J1602.13, J1602.14, R1601.2, R1607.2, R1608.2, R1610.2, R1614.2, R1617.2, U1601.1 (PGND), U1601.6 (AGND), U1601.11 (PGND), U1602.3 (GND), U1603.4 (V-), U1604.3 (GND)
IA_N: J1601.16
IA_P: J1601.15
IB_N: J1601.18
IB_P: J1601.17
ID: J1601.25, R1601.1, R1602.2, R1603.2, R1604.2, R1605.2
K_A_MAIN: J1602.2
K_A_PRE: J1602.1
K_B_MAIN: J1602.4
K_B_PRE: J1602.3
K_DISCH: J1602.5
OV1_OK: U1603.1 (OUTA), U1604.1 (A)
OV1_X: C1609.1, R1609.2, R1610.1, U1603.2 (-INA)
OV1_Y: C1610.1, R1611.2, R1612.1, U1603.3 (+INA)
OV2_OK: U1603.7 (OUTB), U1604.2 (B)
OV2_X: C1611.1, R1613.2, R1614.1, U1603.6 (-INB)
OV2_Y: C1612.1, R1615.2, R1616.1, U1603.5 (+INB)
OV_OK: R1617.1, TP1601.1, U1604.4 (Y)
OV_REF: C1608.1, R1612.2, R1616.2, U1602.2 (OUT)
PE: MH1601.1
SS_BOOT: C1603.1, U1601.4 (BOOT)
SS_FB: R1606.2, R1607.1, U1601.7 (FB)
SS_SW: C1603.2, L1601.1, U1601.12 (SW)
SS_VCC: C1604.1, U1601.5 (VCC)
TRIP_IN: J1603.2, S1602.2 (B)
TRIP_SRC: J1603.1, S1601.1
VAX_N: J1601.8
VAX_P: J1601.7
VA_N: J1601.6, R1611.1
VA_P: J1601.5, R1609.1
VBX_N: J1601.12
VBX_P: J1601.11
VB_N: J1601.10, R1615.1
VB_P: J1601.9, R1613.1

Notes on the sheet:
COOLANT LOOP -> SYS-IO-AUX J801 SPARE TRIP INPUT (ISO1211, 1:1 HARNESS)
port.CTRL_PINS, 14-way, the PV-PORT harness: DO_SPARE = hold-logic proof test of both ports. IMD_SW_P/N not used on DAB60 (no insulation measurement): open.
PORT CONNECTOR (CTRL-C2000), ID WITH HOLD READBACK
LMR36015ARNXR 400 kHz, 10 uH, 100k / 43.2k -> 3.315 V for 4 x AMC3330 + 2 x AMC3302 + port hold logic + OV comparator (SNVSB49D Fig 10-1: 4.7 uF + 220 nF in, 100 nF boot, 1 uF VCC, 2 x 22 uF out). AGND joins GND only here.
Matched dividers on the AMC3330 outputs: OK while VA_P - VA_N < 2.048 V x R1/R2 (common mode rejected); OPA2388 as comparator (VOS 7.5 uV; inputs differ by mV at the trip point). Port 1 trips at 986 V (972-1000 V), port 2 at 937 V (924-950 V): worst case <= the spec 1000 / 950 V, above the firmware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
AUX-HV FEED: PORT 1 ONLY (D-021, INT-11)
AUX-HV PA+ = J1206 on A_X+ (terminal side of port 1: fuse + EMI filter, ahead of the contactor), PA- = J1205 on P1_BUS-. AUX-HV PB+/PB- stay open. Port 2 stud J1406 on B_X+ is DNP: no port-2 tap exists, so HV1 and HV2 never meet in the AUX-HV diode OR. Consequence: no black start from port 2 withou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
interfaces.PORT: VA/VAX/IA = port 1 (tag A), VB/VBX/IB = port 2 (tag B). AUX1/AUX2 not used (no IMD). ID: 2.61k || readback = 2.480 k (code 2.49k). RB1/RB2 of port A via 402k, of port B via 133k: nine levels 0.496-0.632 V within +/-165 mV of the code (PVCELL-25 window starts at 0.667 V); unpowered 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
Flow switch (closed while flow > 6 l/min) in series with the cold-plate thermostat (opens at 77 C): loop open = channel-A hardware trip on SYS-IO-AUX (latched there, no firmware). SYS wets the loop from 24V_OR via 2.2k into the ISO1211 limiter: 0.00-0.00 mA, <= 30 V open. Contacts: reed (VK3, 1 A /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
SYS-IO-AUX HARNESS (COILS, CONTACTOR FEEDBACK, PROOF TEST)
SENSOR SUPPLY +3V3S (PORT_SPEC.JSON SENSOR_SUPPLY)
PORT OVER-VOLTAGE COMPARATORS (BOTH BRIDGES TRIP, LATCHED THERE)
