vectivolt/PCM/hardware/GDRV-HB/sheets/01_interface.kicad_sch

## KiCad design hardware/GDRV-HB/sheets/01_interface.kicad_sch (2026-10-04)

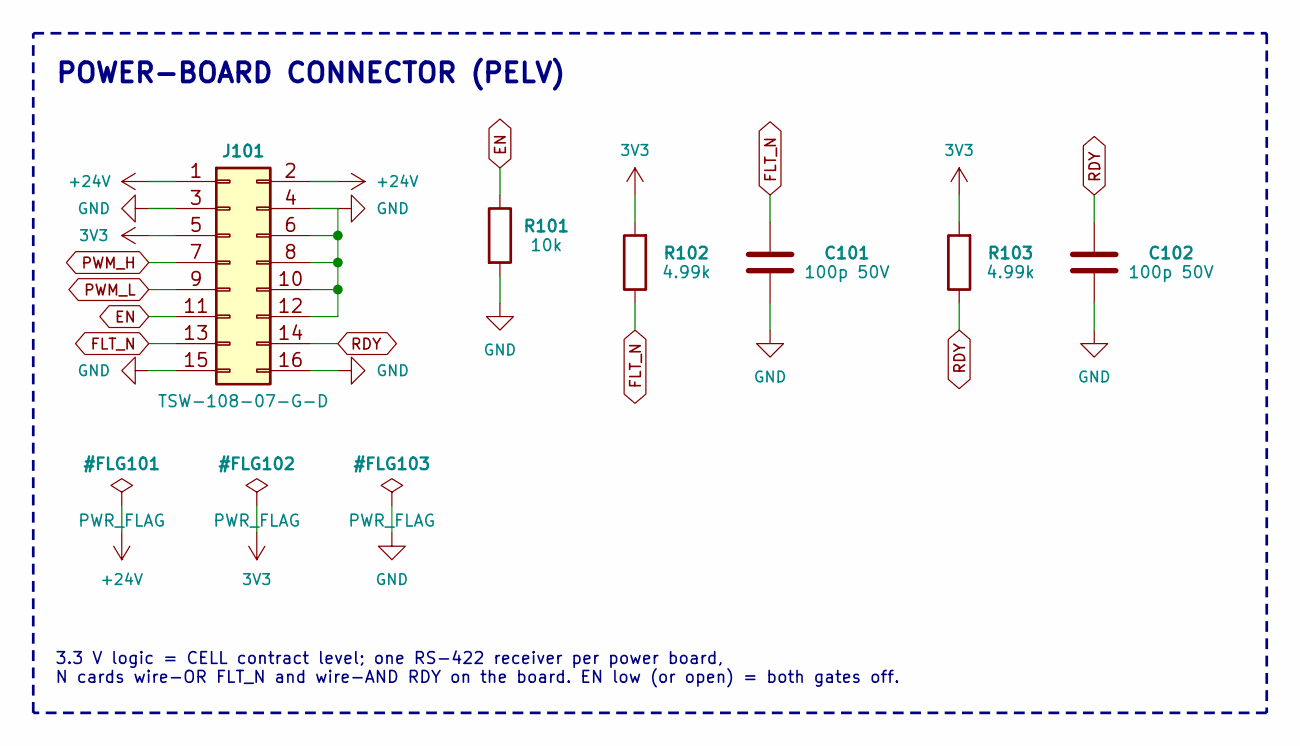
[picture p267: schematic 01_interface.kicad_sch]

Parts:
C101, C102: 100p 50V
J101: TSW-108-07-G-D; MPN TSW-108-07-G-D
R101: 10k
R102, R103: 4.99k

Connections:
3V3: J101.5, R102.2, R103.2
+24V: J101.1, J101.2
EN: J101.11, R101.1
FLT_N: C101.1, J101.13, R102.1
GND: C101.2, C102.2, J101.3, J101.4, J101.6, J101.8, J101.10, J101.12, J101.15, J101.16, R101.2
PWM_H: J101.7
PWM_L: J101.9
RDY: C102.1, J101.14, R103.1

Notes on the sheet:
3.3 V logic = CELL contract level; one RS-422 receiver per power board, N cards wire-OR FLT_N and wire-AND RDY on the board. EN low (or open) = both gates off.
POWER-BOARD CONNECTOR (PELV)
