vectivolt/PCM/hardware/GDRV-HB/sheets/02_high.kicad_sch

## KiCad design hardware/GDRV-HB/sheets/02_high.kicad_sch (2026-10-07)

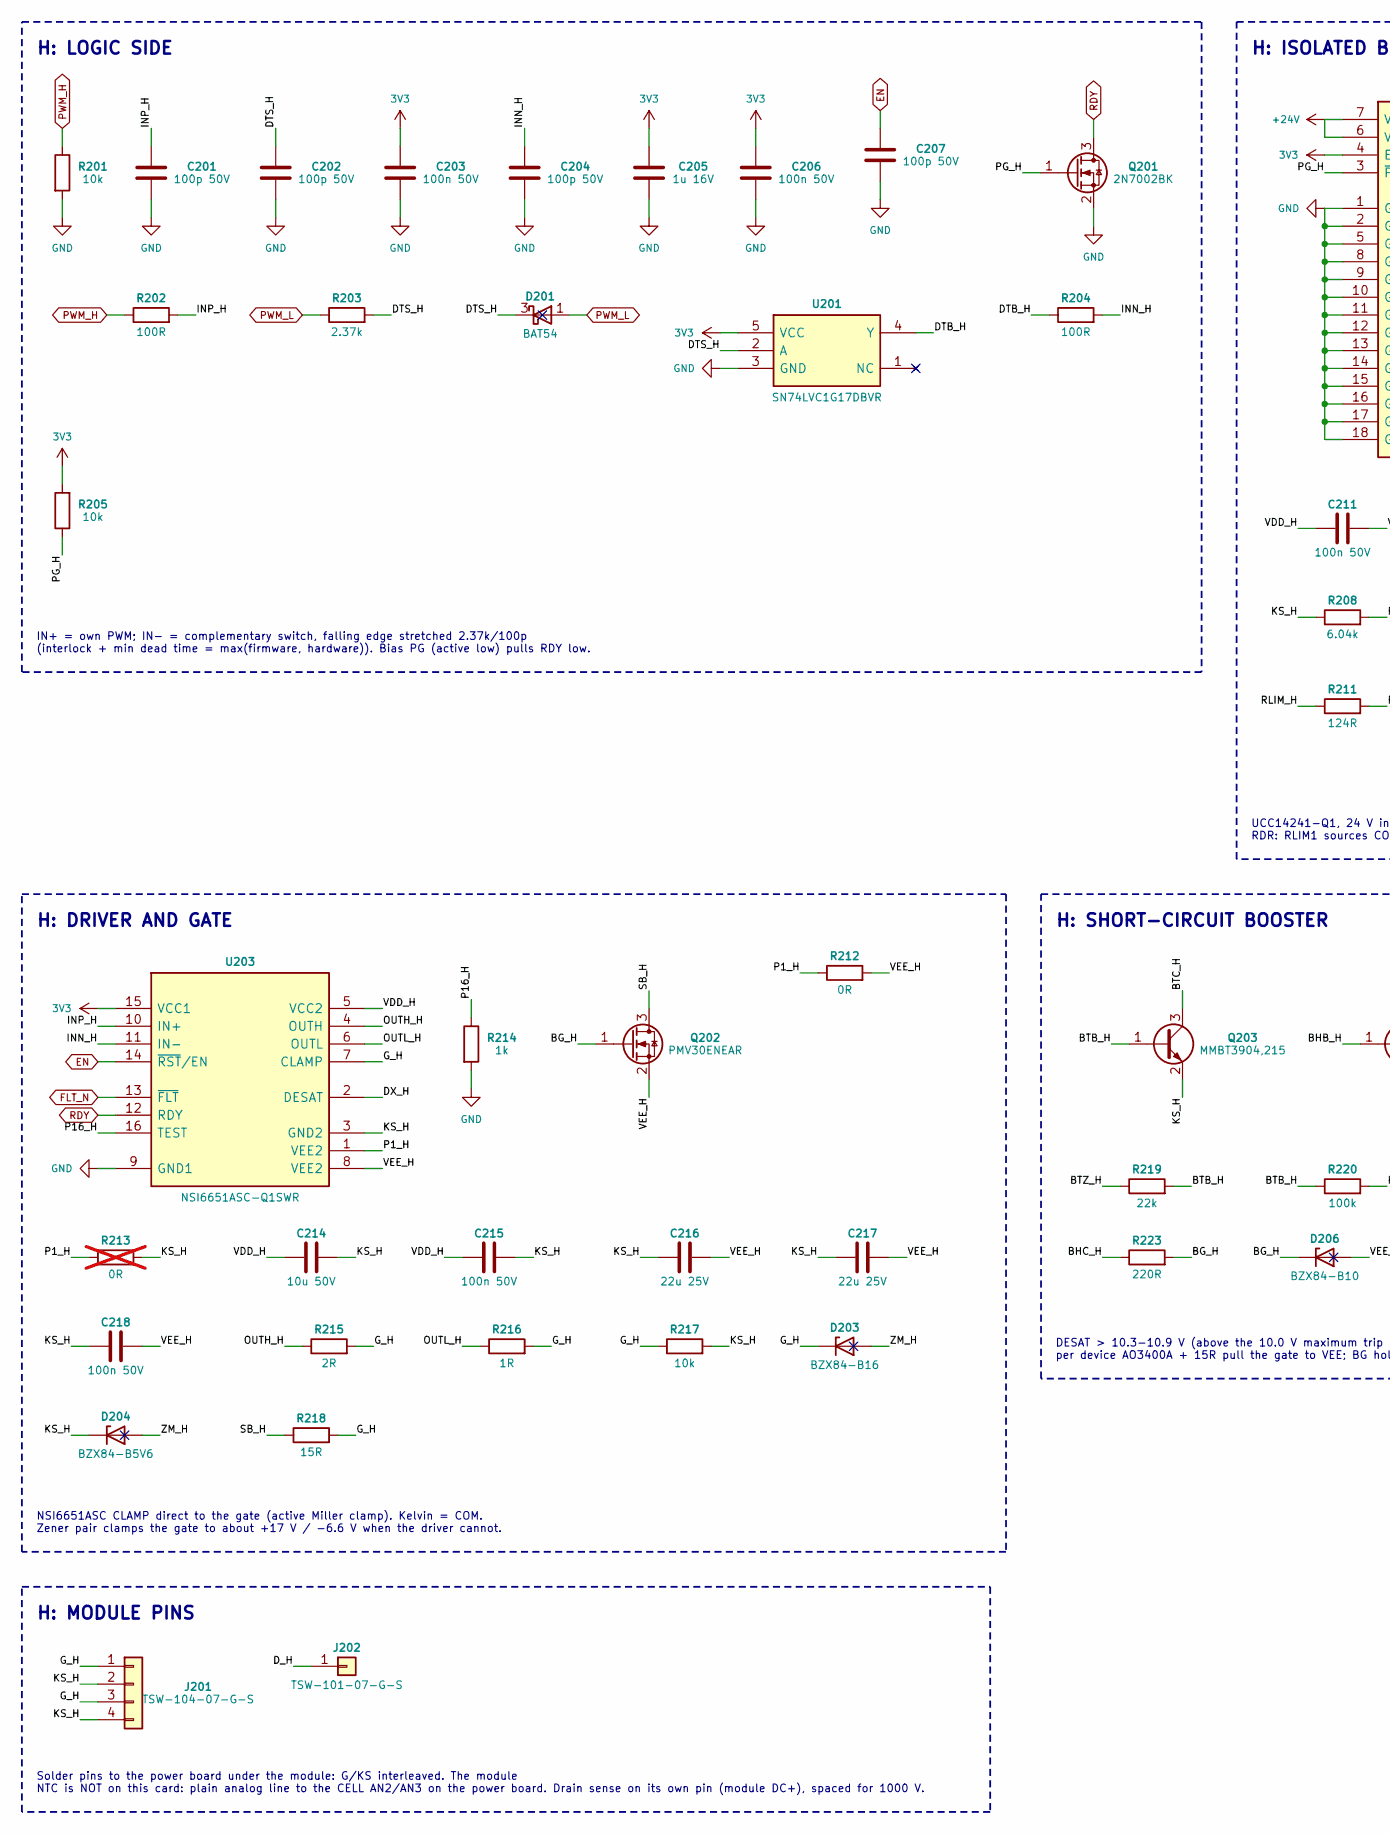
[picture p268: schematic 02_high.kicad_sch, part in row 1, column 1]

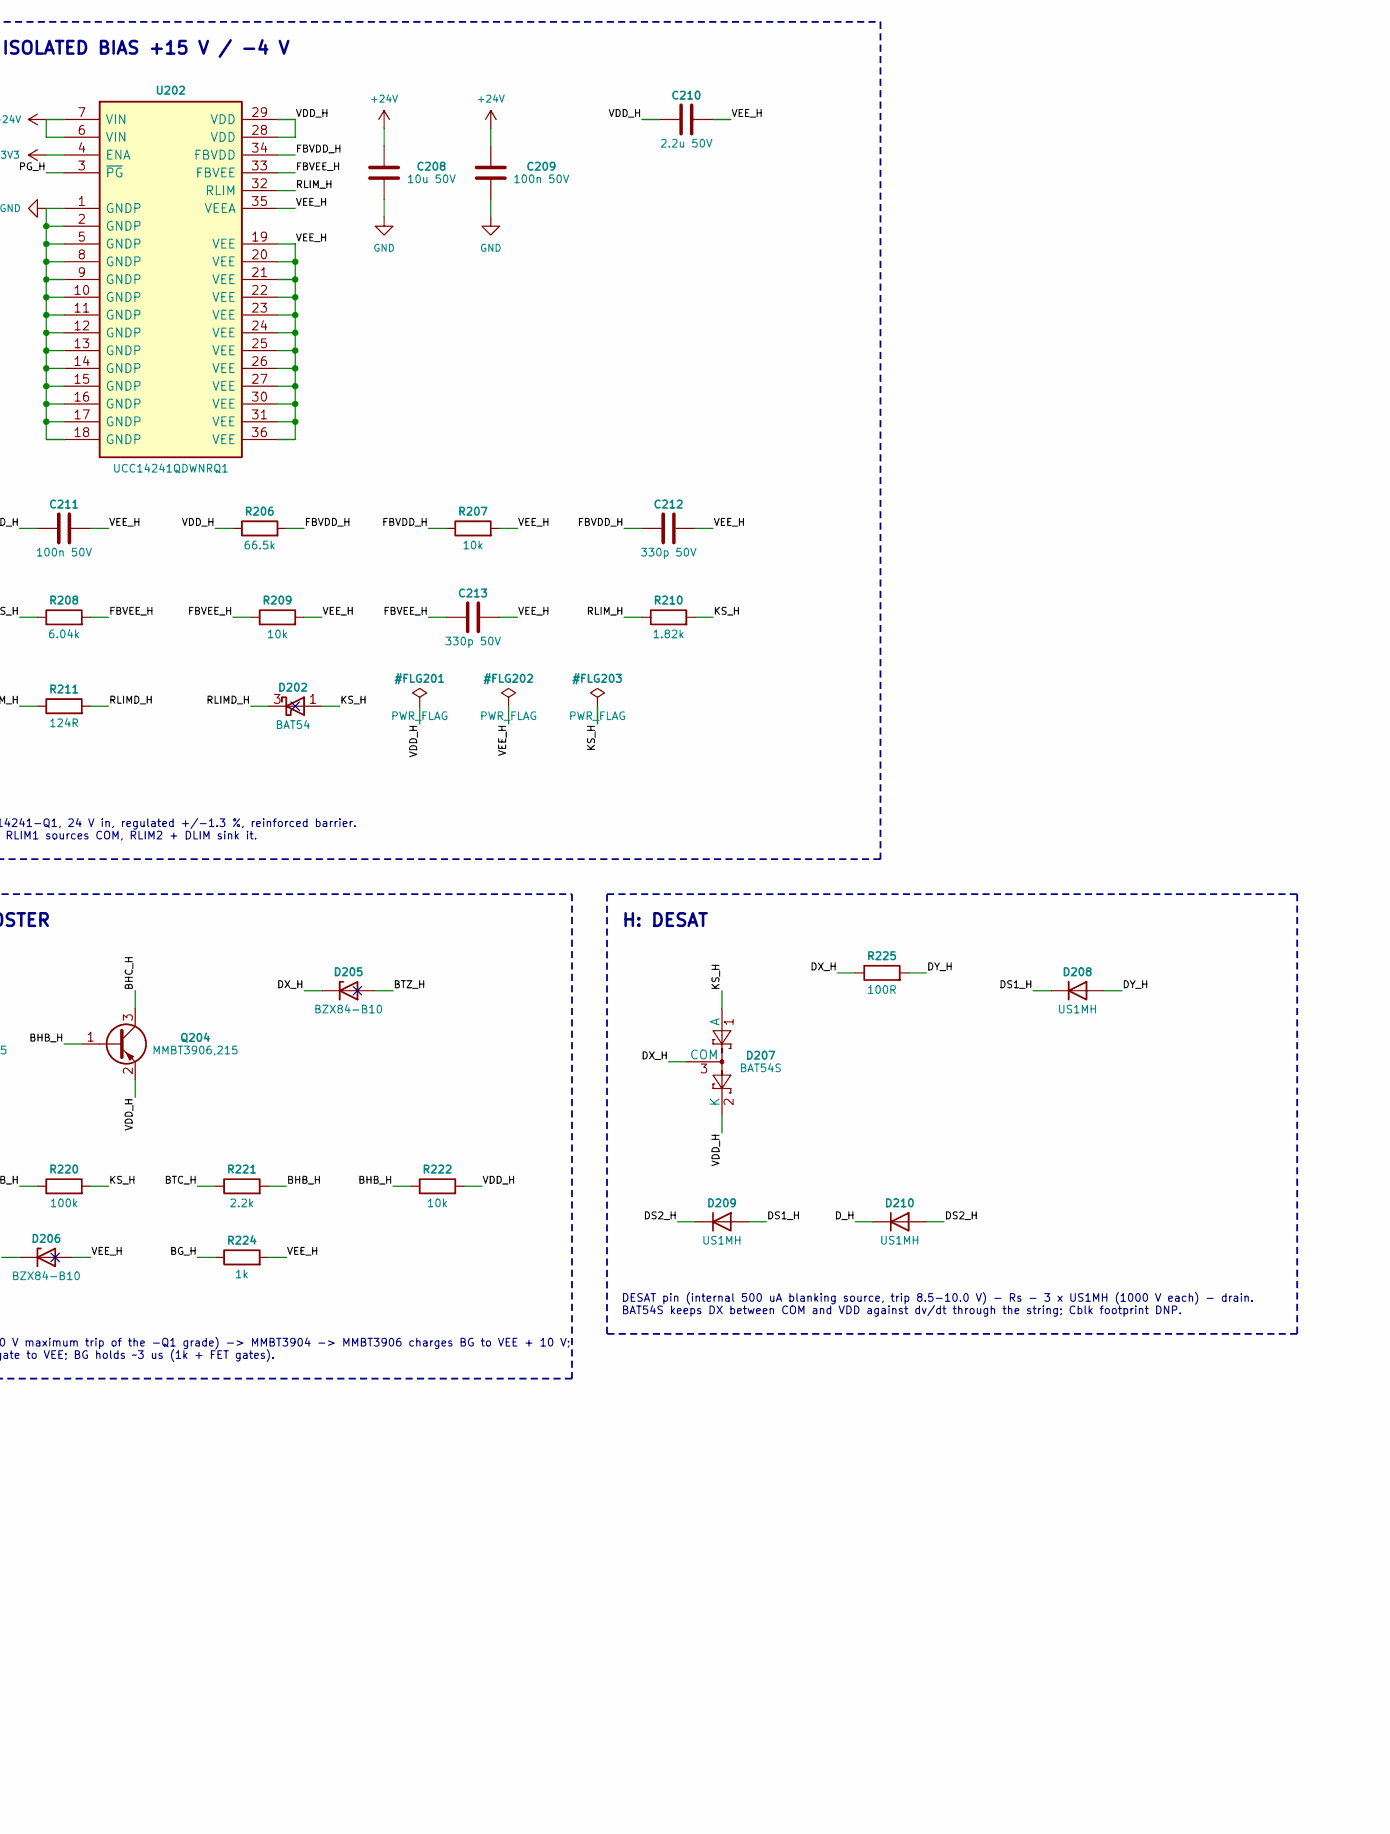
[picture p269: schematic 02_high.kicad_sch, part in row 1, column 2]

Parts:
C201, C202, C204, C207: 100p 50V
C203, C206, C209, C211, C215, C218: 100n 50V
C205: 1u 16V
C208, C214: 10u 50V
C210: 2.2u 50V
C212, C213: 330p 50V
C216, C217: 22u 25V
D201, D202: BAT54; MPN BAT54
D203: BZX84-B16; MPN BZX84-B16
D204: BZX84-B5V6; MPN BZX84-B5V6
D205, D206: BZX84-B10; MPN BZX84-B10
D207: BAT54S; MPN BAT54S
D208, D209, D210: US1MH; MPN US1MH
J201: TSW-104-07-G-S; MPN TSW-104-07-G-S
J202: TSW-101-07-G-S; MPN TSW-101-07-G-S
Q201: 2N7002BK; MPN 2N7002BK
Q202: PMV30ENEAR; MPN PMV30ENEAR
Q203: MMBT3904,215; MPN MMBT3904,215
Q204: MMBT3906,215; MPN MMBT3906,215
R201, R205, R207, R209, R217, R222: 10k
R202, R204, R225: 100R
R203: 2.37k
R206: 66.5k
R208: 6.04k
R210: 1.82k
R211: 124R
R212: 0R
R213: 0R; not fitted
R214, R224: 1k
R215: 2R
R216: 1R
R218: 15R
R219: 22k
R220: 100k
R221: 2.2k
R223: 220R
U201: SN74LVC1G17DBVR; MPN SN74LVC1G17DBVR
U202: UCC14241QDWNRQ1; MPN UCC14241QDWNRQ1
U203: NSI6651ASC-Q1SWR; MPN NSI6651ASC-Q1SWR

Connections:
3V3: C203.1, C205.1, C206.1, R205.2, U201.5 (VCC), U202.4 (ENA), U203.15 (VCC1)
+24V: C208.1, C209.1, U202.6 (VIN), U202.7 (VIN)
BG_H: D206.3 (K), Q202.1 (G), R223.2, R224.1
BHB_H: Q204.1 (B), R221.2, R222.1
BHC_H: Q204.3 (C), R223.1
BTB_H: Q203.1 (B), R219.2, R220.1
BTC_H: Q203.3 (C), R221.1
BTZ_H: D205.1 (A), R219.1
DS1_H: D208.1 (K), D209.2 (A)
DS2_H: D209.1 (K), D210.2 (A)
DTB_H: R204.1, U201.4 (Y)
DTS_H: C202.1, D201.3 (K), R203.2, U201.2 (A)
DX_H: D205.3 (K), D207.3 (COM), R225.1, U203.2 (DESAT)
DY_H: D208.2 (A), R225.2
D_H: D210.1 (K), J202.1
EN: C207.1, U203.14 (~RST/EN)
FBVDD_H: C212.1, R206.2, R207.1, U202.34 (FBVDD)
FBVEE_H: C213.1, R208.2, R209.1, U202.33 (FBVEE)
FLT_N: U203.13 (~FLT)
GND: C201.2, C202.2, C203.2, C204.2, C205.2, C206.2, C207.2, C208.2, C209.2, Q201.2 (S), R201.2, R214.2, U201.3 (GND), U202.1 (GNDP), U202.2 (GNDP), U202.5 (GNDP), U202.8 (GNDP), U202.9 (GNDP), U202.10 (GNDP), U202.11 (GNDP), U202.12 (GNDP), U202.13 (GNDP), U202.14 (GNDP), U202.15 (GNDP), U202.16 (GNDP), U202.17 (GNDP), U202.18 (GNDP), U203.9 (GND1)
G_H: D203.3 (K), J201.1, J201.3, R215.2, R216.2, R217.1, R218.2, U203.7 (CLAMP)
INN_H: C204.1, R204.2, U203.11 (IN-)
INP_H: C201.1, R202.2, U203.10 (IN+)
KS_H: C214.2, C215.2, C216.1, C217.1, C218.1, D202.1 (A), D204.3 (K), D207.1 (A), J201.2, J201.4, Q203.2 (E), R208.1, R210.2, R213.2, R217.2, R220.2, U203.3 (GND2)
OUTH_H: R215.1, U203.4 (OUTH)
OUTL_H: R216.1, U203.6 (OUTL)
P1_H: R212.1, R213.1, U203.1 (VEE2)
P16_H: R214.1, U203.16 (TEST)
PG_H: Q201.1 (G), R205.1, U202.3 (~PG)
PWM_H: R201.1, R202.1
PWM_L: D201.1 (A), R203.1
RDY: Q201.3 (D), U203.12 (RDY)
RLIMD_H: D202.3 (K), R211.2
RLIM_H: R210.1, R211.1, U202.32 (RLIM)
SB_H: Q202.3 (D), R218.1
VDD_H: C210.1, C211.1, C214.1, C215.1, D207.2 (K), Q204.2 (E), R206.1, R222.2, U202.28 (VDD), U202.29 (VDD), U203.5 (VCC2)
VEE_H: C210.2, C211.2, C212.2, C213.2, C216.2, C217.2, C218.2, D206.1 (A), Q202.2 (S), R207.2, R209.2, R212.2, R224.2, U202.19 (VEE), U202.20 (VEE), U202.21 (VEE), U202.22 (VEE), U202.23 (VEE), U202.24 (VEE), U202.25 (VEE), U202.26 (VEE), U202.27 (VEE), U202.30 (VEE), U202.31 (VEE), U202.35 (VEEA), U202.36 (VEE), U203.8 (VEE2)
ZM_H: D203.1 (A), D204.1 (A)

Notes on the sheet:
IN+ = own PWM; IN- = complementary switch, falling edge stretched 2.37k/100p (interlock + min dead time = max(firmware, hardware)). Bias PG (active low) pulls RDY low.
H: DESAT
H: ISOLATED BIAS +15 V / -4 V
Solder pins to the power board under the module: G/KS interleaved. The module NTC is NOT on this card: plain analog line to the CELL AN2/AN3 on the power board. Drain sense on its own pin (module DC+), spaced for 1000 V.
H: SHORT-CIRCUIT BOOSTER
H: DRIVER AND GATE
H: LOGIC SIDE
H: MODULE PINS
DESAT > 10.3-10.9 V (above the 10.0 V maximum trip of the -Q1 grade) -> MMBT3904 -> MMBT3906 charges BG to VEE + 10 V; per device AO3400A + 15R pull the gate to VEE; BG holds ~3 us (1k + FET gates).
NSI6651ASC CLAMP direct to the gate (active Miller clamp). Kelvin = COM. Zener pair clamps the gate to about +17 V / -6.6 V when the driver cannot.
UCC14241-Q1, 24 V in, regulated +/-1.3 %, reinforced barrier. RDR: RLIM1 sources COM, RLIM2 + DLIM sink it.
DESAT pin (internal 500 uA blanking source, trip 8.5-10.0 V) - Rs - 3 x US1MH (1000 V each) - drain. BAT54S keeps DX between COM and VDD against dv/dt through the string; Cblk footprint DNP.
