vectivolt/PCM/hardware/GDRV-HB/sheets/03_low.kicad_sch

## KiCad design hardware/GDRV-HB/sheets/03_low.kicad_sch (2026-10-07)

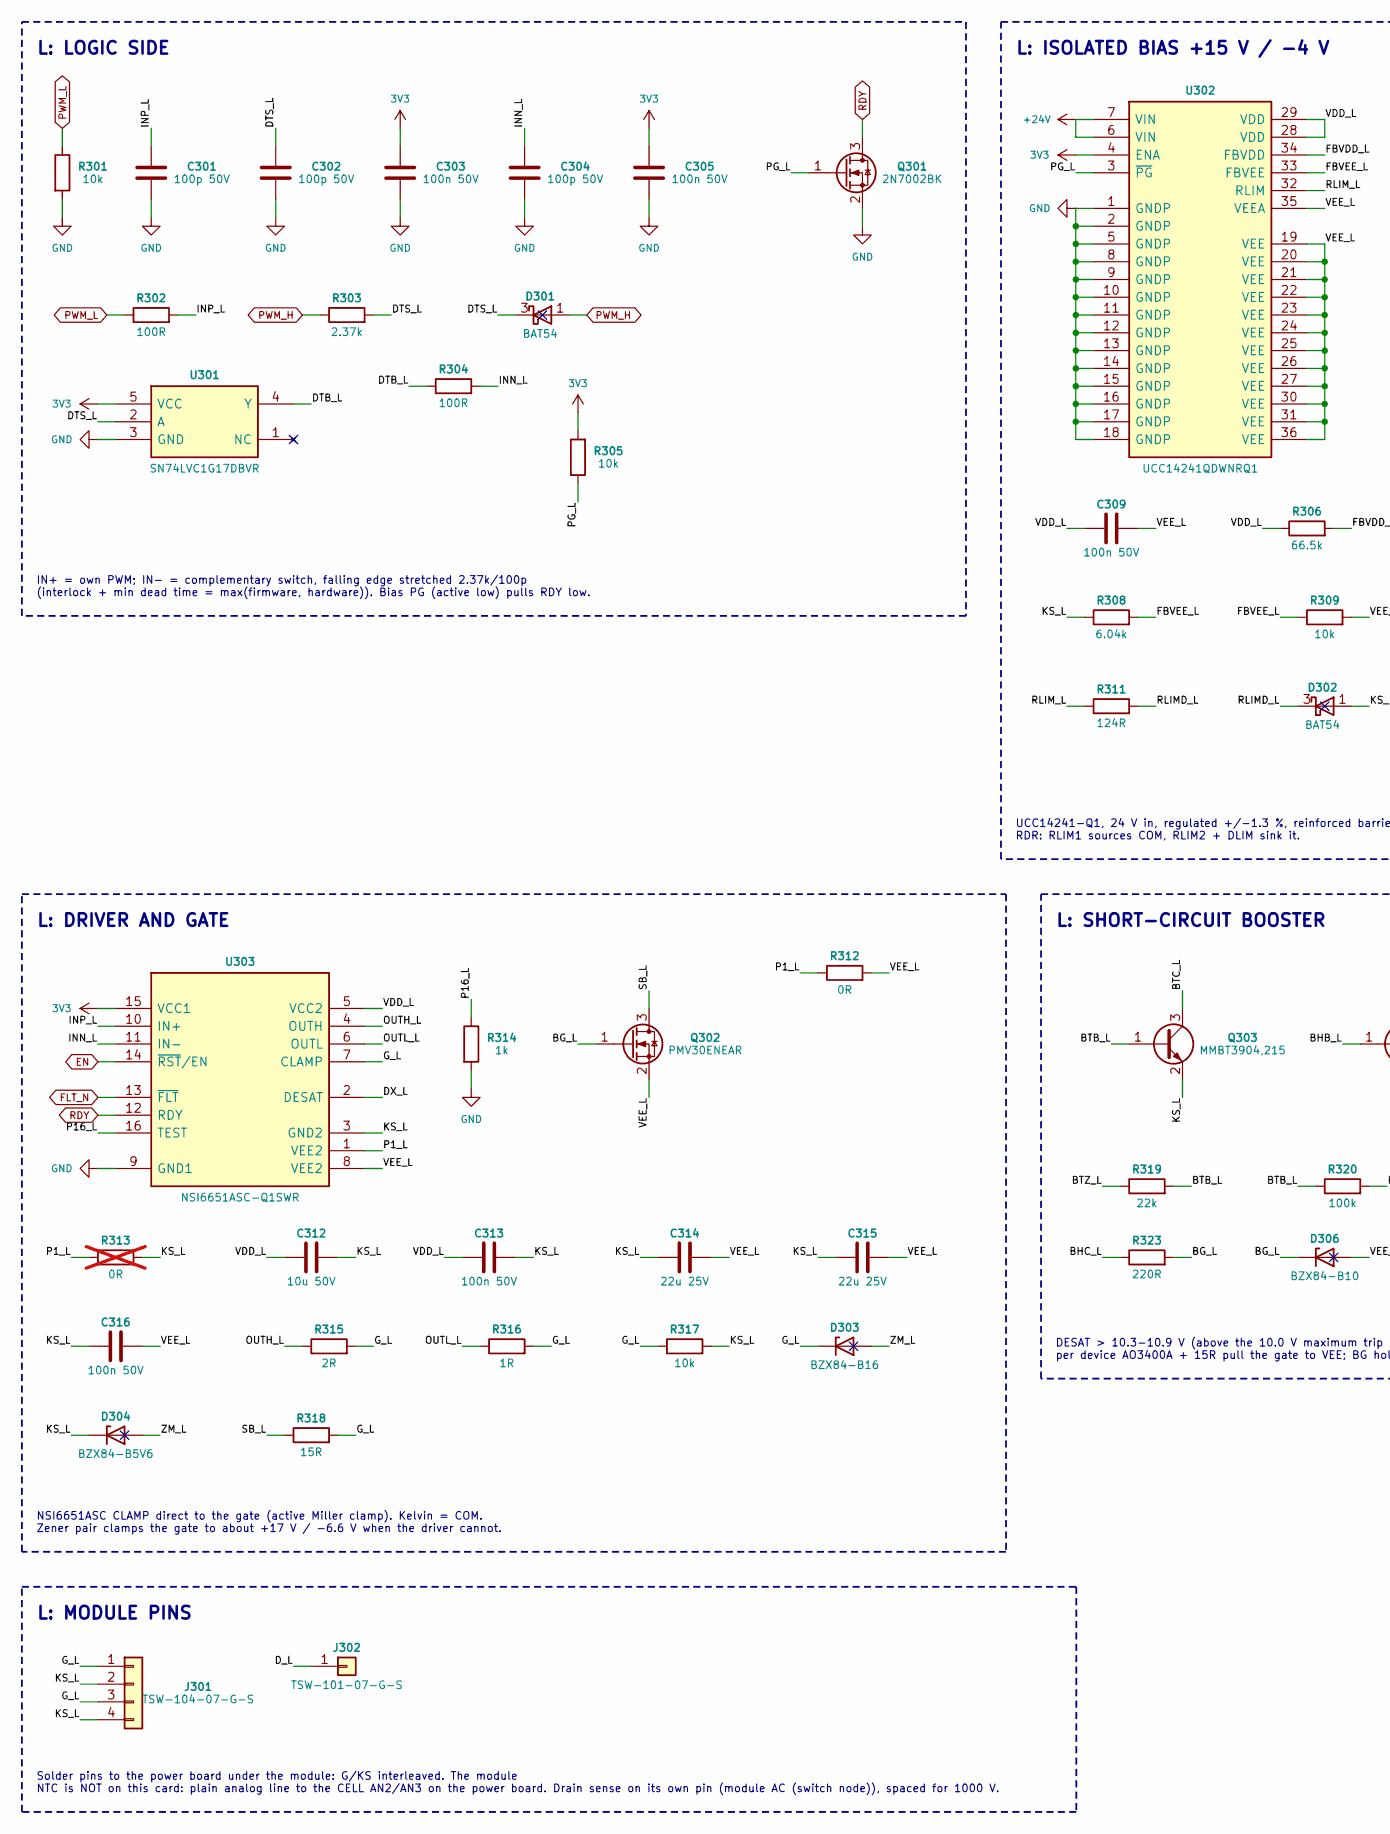
[picture p270: schematic 03_low.kicad_sch, part in row 1, column 1]

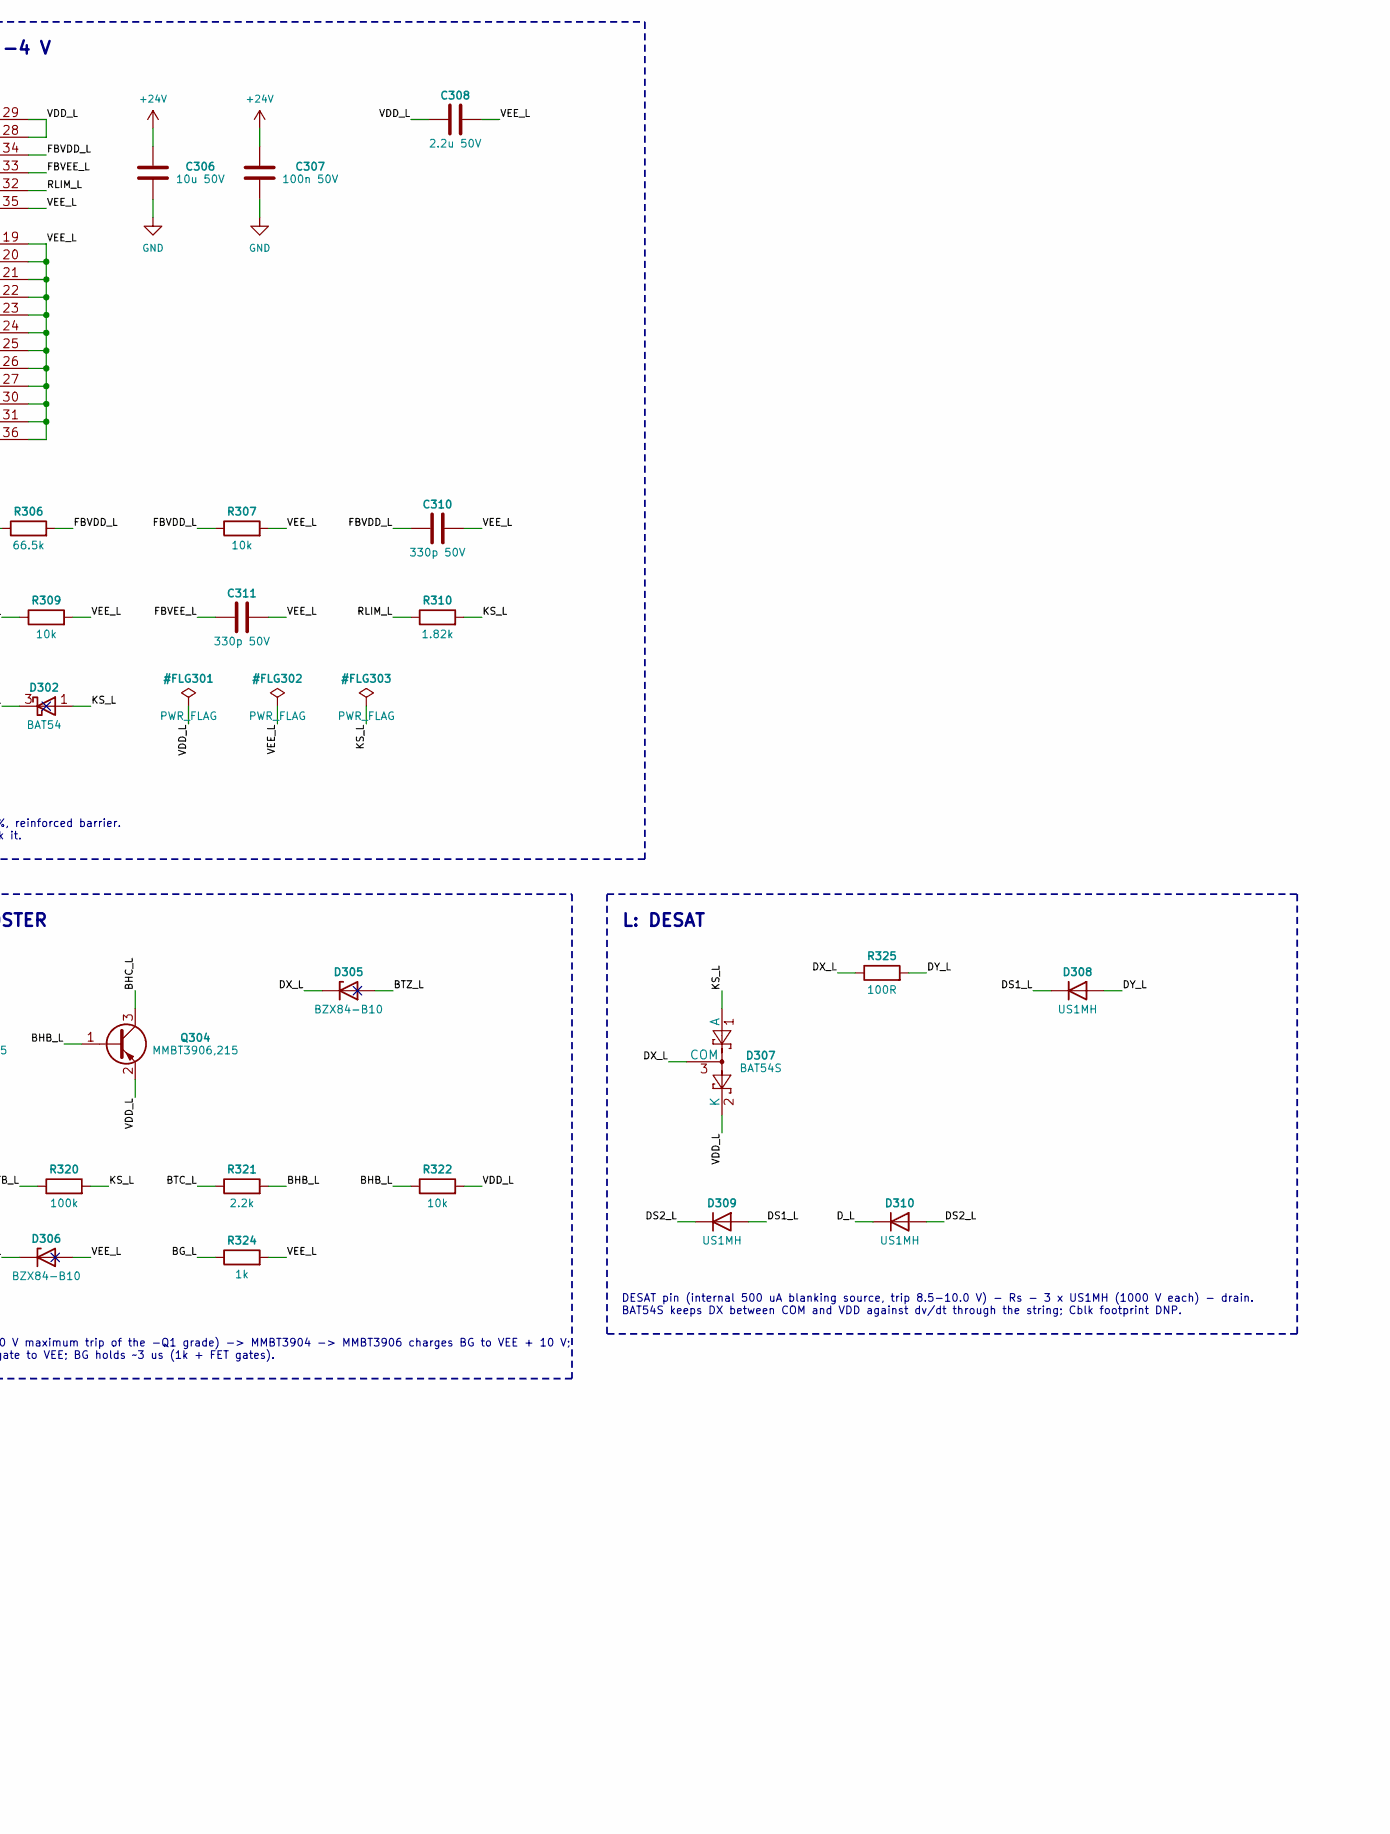
[picture p271: schematic 03_low.kicad_sch, part in row 1, column 2]

Parts:
C301, C302, C304: 100p 50V
C303, C305, C307, C309, C313, C316: 100n 50V
C306, C312: 10u 50V
C308: 2.2u 50V
C310, C311: 330p 50V
C314, C315: 22u 25V
D301, D302: BAT54; MPN BAT54
D303: BZX84-B16; MPN BZX84-B16
D304: BZX84-B5V6; MPN BZX84-B5V6
D305, D306: BZX84-B10; MPN BZX84-B10
D307: BAT54S; MPN BAT54S
D308, D309, D310: US1MH; MPN US1MH
J301: TSW-104-07-G-S; MPN TSW-104-07-G-S
J302: TSW-101-07-G-S; MPN TSW-101-07-G-S
Q301: 2N7002BK; MPN 2N7002BK
Q302: PMV30ENEAR; MPN PMV30ENEAR
Q303: MMBT3904,215; MPN MMBT3904,215
Q304: MMBT3906,215; MPN MMBT3906,215
R301, R305, R307, R309, R317, R322: 10k
R302, R304, R325: 100R
R303: 2.37k
R306: 66.5k
R308: 6.04k
R310: 1.82k
R311: 124R
R312: 0R
R313: 0R; not fitted
R314, R324: 1k
R315: 2R
R316: 1R
R318: 15R
R319: 22k
R320: 100k
R321: 2.2k
R323: 220R
U301: SN74LVC1G17DBVR; MPN SN74LVC1G17DBVR
U302: UCC14241QDWNRQ1; MPN UCC14241QDWNRQ1
U303: NSI6651ASC-Q1SWR; MPN NSI6651ASC-Q1SWR

Connections:
3V3: C303.1, C305.1, R305.2, U301.5 (VCC), U302.4 (ENA), U303.15 (VCC1)
+24V: C306.1, C307.1, U302.6 (VIN), U302.7 (VIN)
BG_L: D306.3 (K), Q302.1 (G), R323.2, R324.1
BHB_L: Q304.1 (B), R321.2, R322.1
BHC_L: Q304.3 (C), R323.1
BTB_L: Q303.1 (B), R319.2, R320.1
BTC_L: Q303.3 (C), R321.1
BTZ_L: D305.1 (A), R319.1
DS1_L: D308.1 (K), D309.2 (A)
DS2_L: D309.1 (K), D310.2 (A)
DTB_L: R304.1, U301.4 (Y)
DTS_L: C302.1, D301.3 (K), R303.2, U301.2 (A)
DX_L: D305.3 (K), D307.3 (COM), R325.1, U303.2 (DESAT)
DY_L: D308.2 (A), R325.2
D_L: D310.1 (K), J302.1
EN: U303.14 (~RST/EN)
FBVDD_L: C310.1, R306.2, R307.1, U302.34 (FBVDD)
FBVEE_L: C311.1, R308.2, R309.1, U302.33 (FBVEE)
FLT_N: U303.13 (~FLT)
GND: C301.2, C302.2, C303.2, C304.2, C305.2, C306.2, C307.2, Q301.2 (S), R301.2, R314.2, U301.3 (GND), U302.1 (GNDP), U302.2 (GNDP), U302.5 (GNDP), U302.8 (GNDP), U302.9 (GNDP), U302.10 (GNDP), U302.11 (GNDP), U302.12 (GNDP), U302.13 (GNDP), U302.14 (GNDP), U302.15 (GNDP), U302.16 (GNDP), U302.17 (GNDP), U302.18 (GNDP), U303.9 (GND1)
G_L: D303.3 (K), J301.1, J301.3, R315.2, R316.2, R317.1, R318.2, U303.7 (CLAMP)
INN_L: C304.1, R304.2, U303.11 (IN-)
INP_L: C301.1, R302.2, U303.10 (IN+)
KS_L: C312.2, C313.2, C314.1, C315.1, C316.1, D302.1 (A), D304.3 (K), D307.1 (A), J301.2, J301.4, Q303.2 (E), R308.1, R310.2, R313.2, R317.2, R320.2, U303.3 (GND2)
OUTH_L: R315.1, U303.4 (OUTH)
OUTL_L: R316.1, U303.6 (OUTL)
P1_L: R312.1, R313.1, U303.1 (VEE2)
P16_L: R314.1, U303.16 (TEST)
PG_L: Q301.1 (G), R305.1, U302.3 (~PG)
PWM_H: D301.1 (A), R303.1
PWM_L: R301.1, R302.1
RDY: Q301.3 (D), U303.12 (RDY)
RLIMD_L: D302.3 (K), R311.2
RLIM_L: R310.1, R311.1, U302.32 (RLIM)
SB_L: Q302.3 (D), R318.1
VDD_L: C308.1, C309.1, C312.1, C313.1, D307.2 (K), Q304.2 (E), R306.1, R322.2, U302.28 (VDD), U302.29 (VDD), U303.5 (VCC2)
VEE_L: C308.2, C309.2, C310.2, C311.2, C314.2, C315.2, C316.2, D306.1 (A), Q302.2 (S), R307.2, R309.2, R312.2, R324.2, U302.19 (VEE), U302.20 (VEE), U302.21 (VEE), U302.22 (VEE), U302.23 (VEE), U302.24 (VEE), U302.25 (VEE), U302.26 (VEE), U302.27 (VEE), U302.30 (VEE), U302.31 (VEE), U302.35 (VEEA), U302.36 (VEE), U303.8 (VEE2)
ZM_L: D303.1 (A), D304.1 (A)

Notes on the sheet:
L: DRIVER AND GATE
L: DESAT
L: MODULE PINS
NSI6651ASC CLAMP direct to the gate (active Miller clamp). Kelvin = COM. Zener pair clamps the gate to about +17 V / -6.6 V when the driver cannot.
IN+ = own PWM; IN- = complementary switch, falling edge stretched 2.37k/100p (interlock + min dead time = max(firmware, hardware)). Bias PG (active low) pulls RDY low.
UCC14241-Q1, 24 V in, regulated +/-1.3 %, reinforced barrier. RDR: RLIM1 sources COM, RLIM2 + DLIM sink it.
DESAT pin (internal 500 uA blanking source, trip 8.5-10.0 V) - Rs - 3 x US1MH (1000 V each) - drain. BAT54S keeps DX between COM and VDD against dv/dt through the string; Cblk footprint DNP.
DESAT > 10.3-10.9 V (above the 10.0 V maximum trip of the -Q1 grade) -> MMBT3904 -> MMBT3906 charges BG to VEE + 10 V; per device AO3400A + 15R pull the gate to VEE; BG holds ~3 us (1k + FET gates).
L: SHORT-CIRCUIT BOOSTER
L: ISOLATED BIAS +15 V / -4 V
Solder pins to the power board under the module: G/KS interleaved. The module NTC is NOT on this card: plain analog line to the CELL AN2/AN3 on the power board. Drain sense on its own pin (module AC (switch node)), spaced for 1000 V.
L: LOGIC SIDE
