vectivolt/PCM/hardware/PCS-CTL/sheets/01_supply.kicad_sch

## KiCad design hardware/PCS-CTL/sheets/01_supply.kicad_sch (2026-10-05)

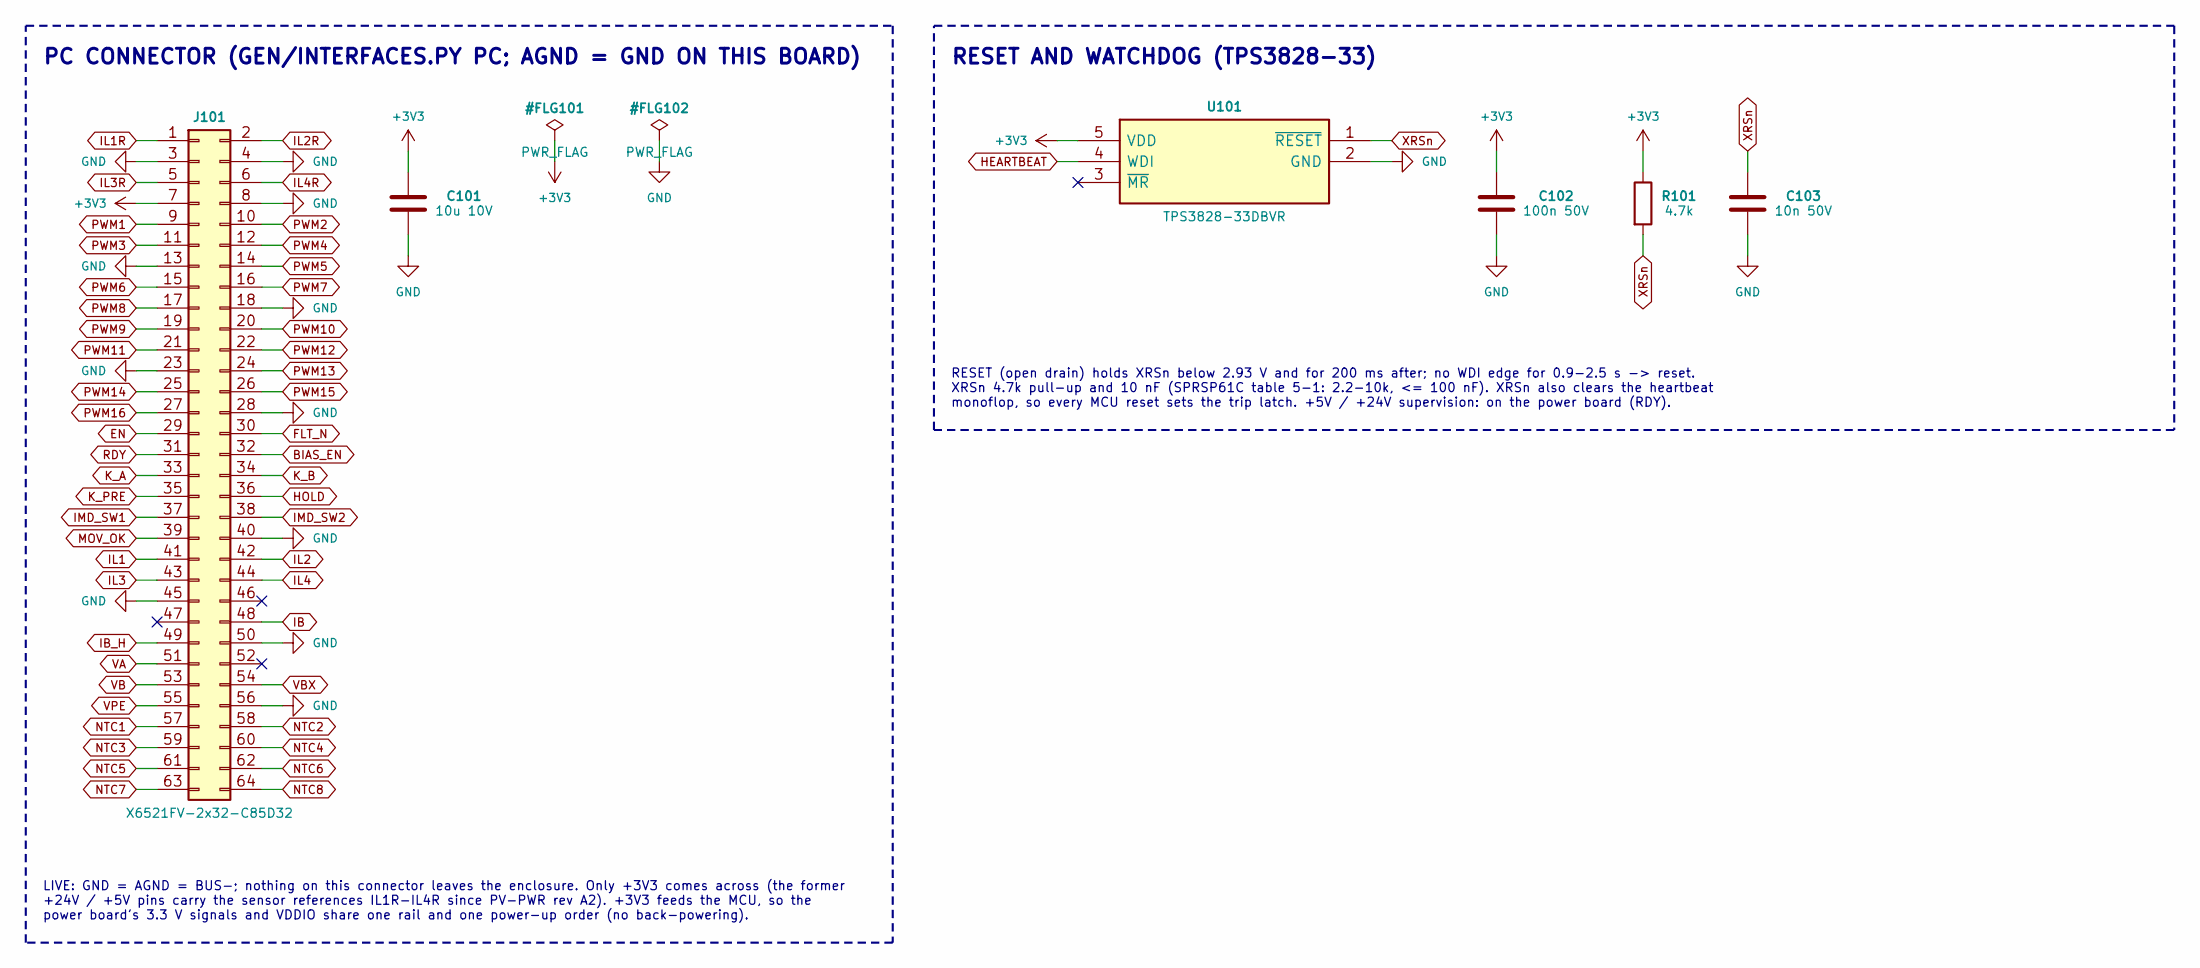
[picture p272: schematic 01_supply.kicad_sch]

Parts:
C101: 10u 10V
C102: 100n 50V
C103: 10n 50V
J101: X6521FV-2x32-C85D32; MPN X6521FV-2x32-C85D32
R101: 4.7k
U101: TPS3828-33DBVR; MPN TPS3828-33DBVR

Connections:
+3V3: C101.1, C102.1, J101.7, R101.1, U101.5 (VDD)
BIAS_EN: J101.32
EN: J101.29
FLT_N: J101.30
GND: C101.2, C102.2, C103.2, J101.3, J101.4, J101.8, J101.13, J101.18, J101.23, J101.28, J101.40, J101.45, J101.50, J101.56, U101.2 (GND)
HEARTBEAT: U101.4 (WDI)
HOLD: J101.36
IB: J101.48
IB_H: J101.49
IL1: J101.41
IL1R: J101.1
IL2: J101.42
IL2R: J101.2
IL3: J101.43
IL3R: J101.5
IL4: J101.44
IL4R: J101.6
IMD_SW1: J101.37
IMD_SW2: J101.38
K_A: J101.33
K_B: J101.34
K_PRE: J101.35
MOV_OK: J101.39
NTC1: J101.57
NTC2: J101.58
NTC3: J101.59
NTC4: J101.60
NTC5: J101.61
NTC6: J101.62
NTC7: J101.63
NTC8: J101.64
PWM1: J101.9
PWM2: J101.10
PWM3: J101.11
PWM4: J101.12
PWM5: J101.14
PWM6: J101.15
PWM7: J101.16
PWM8: J101.17
PWM9: J101.19
PWM10: J101.20
PWM11: J101.21
PWM12: J101.22
PWM13: J101.24
PWM14: J101.25
PWM15: J101.26
PWM16: J101.27
RDY: J101.31
VA: J101.51
VB: J101.53
VBX: J101.54
VPE: J101.55
XRSn: C103.1, R101.2, U101.1 (~RESET)

Notes on the sheet:
LIVE: GND = AGND = BUS-; nothing on this connector leaves the enclosure. Only +3V3 comes across (the former +24V / +5V pins carry the sensor references IL1R-IL4R since PV-PWR rev A2). +3V3 feeds the MCU, so the power board's 3.3 V signals and VDDIO share one rail and one power-up order (no back-pow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
RESET AND WATCHDOG (TPS3828-33)
RESET (open drain) holds XRSn below 2.93 V and for 200 ms after; no WDI edge for 0.9-2.5 s -> reset. XRSn 4.7k pull-up and 10 nF (SPRSP61C table 5-1: 2.2-10k, <= 100 nF). XRSn also clears the heartbeat monoflop, so every MCU reset sets the trip latch. +5V / +24V supervision: on the power board (RDY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
PC CONNECTOR (GEN/INTERFACES.PY PC; AGND = GND ON THIS BOARD)
