vectivolt/PCM/hardware/PCS-CTL/sheets/02_mcu.kicad_sch

## KiCad design hardware/PCS-CTL/sheets/02_mcu.kicad_sch (2026-10-06)

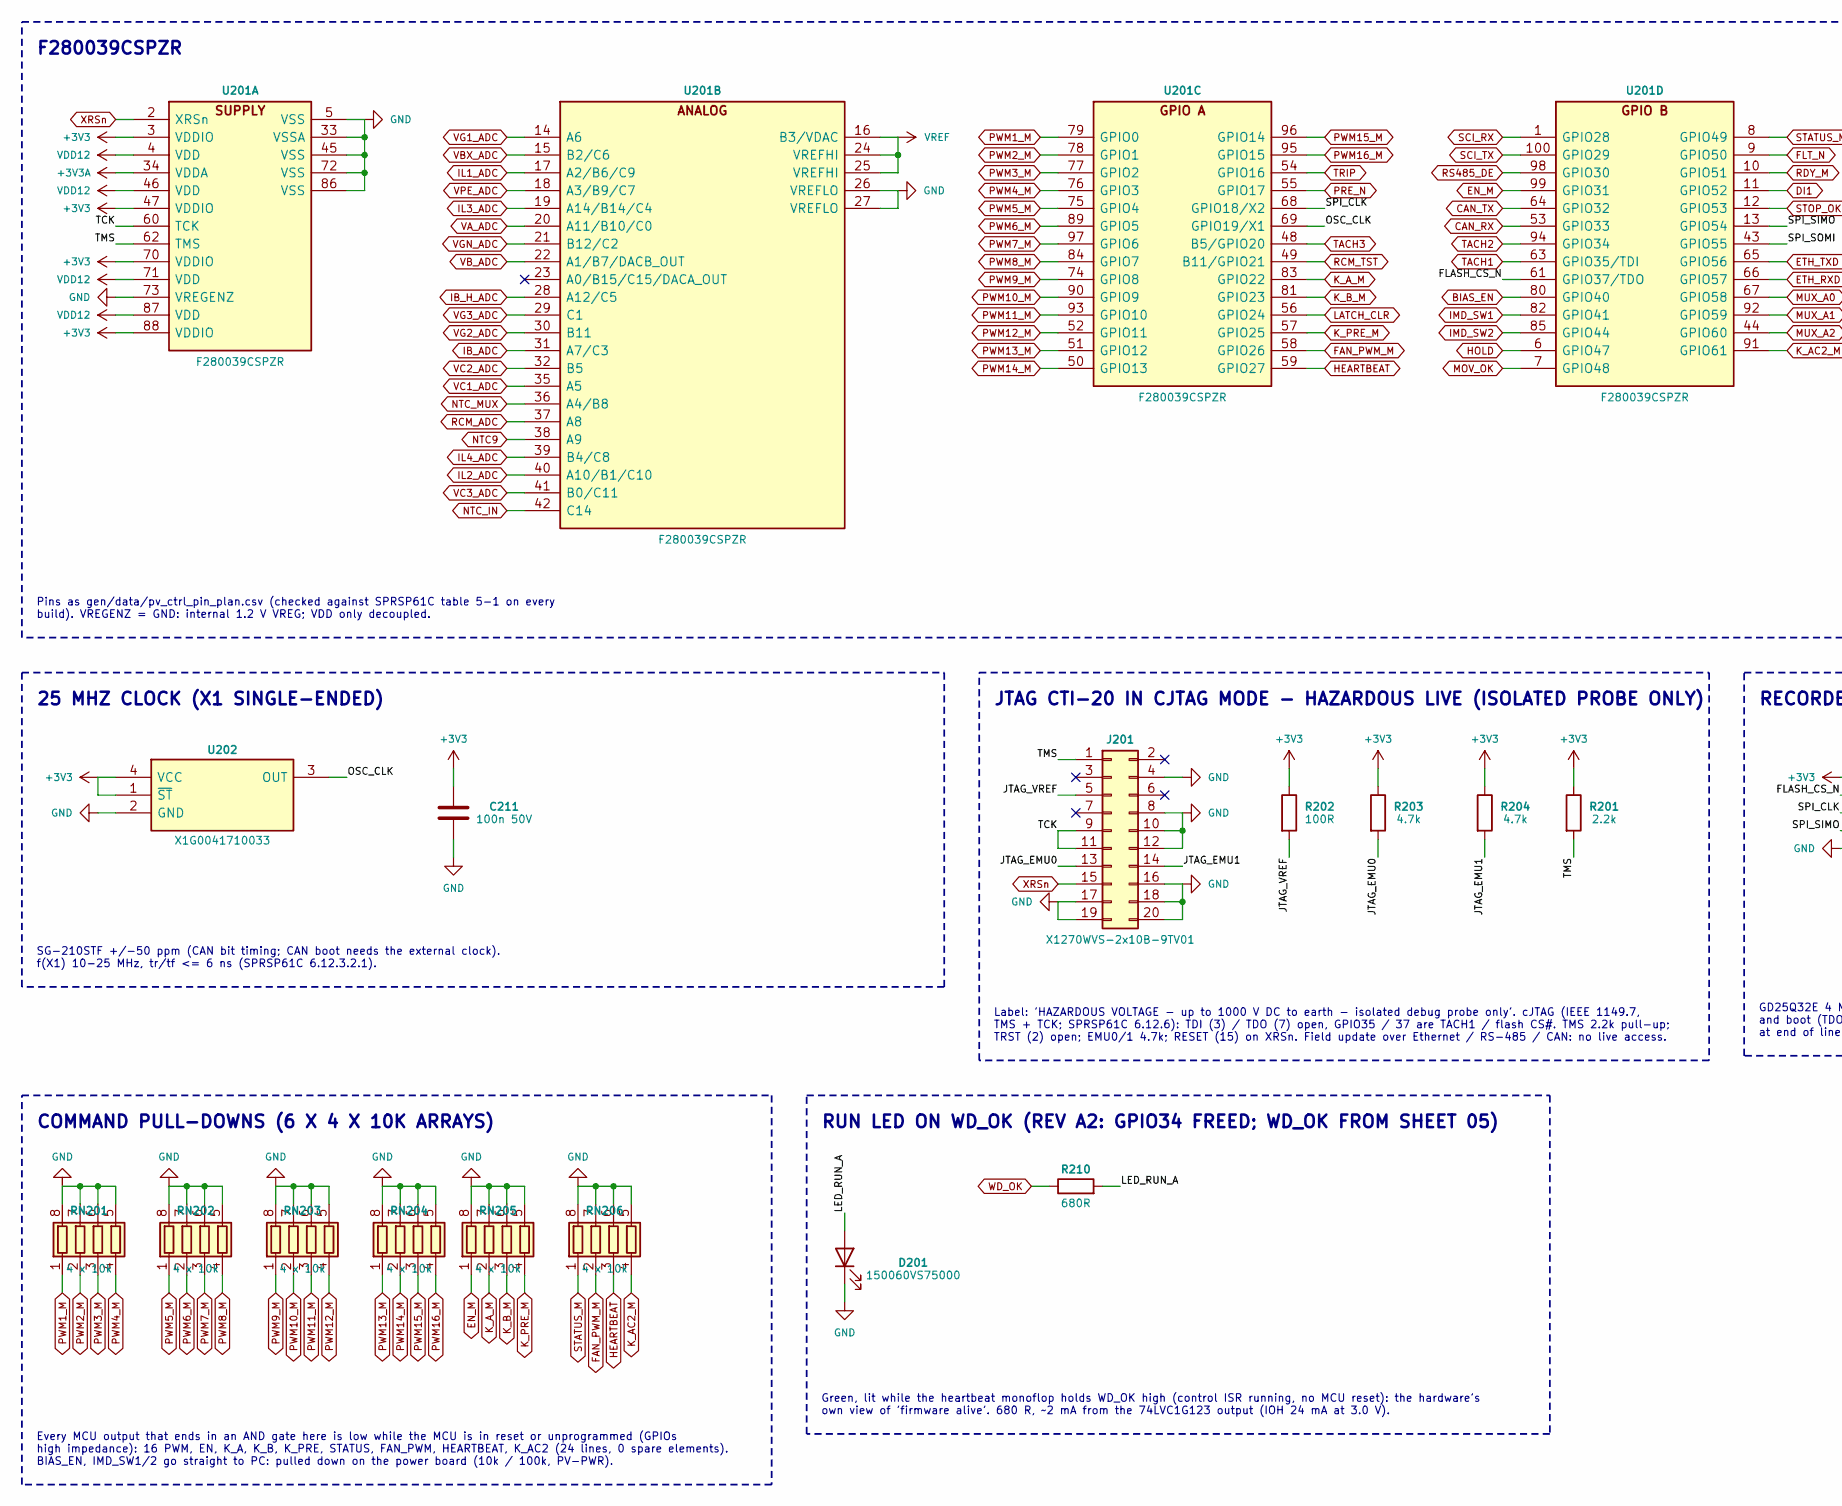
[picture p273: schematic 02_mcu.kicad_sch, part in row 1, column 1]

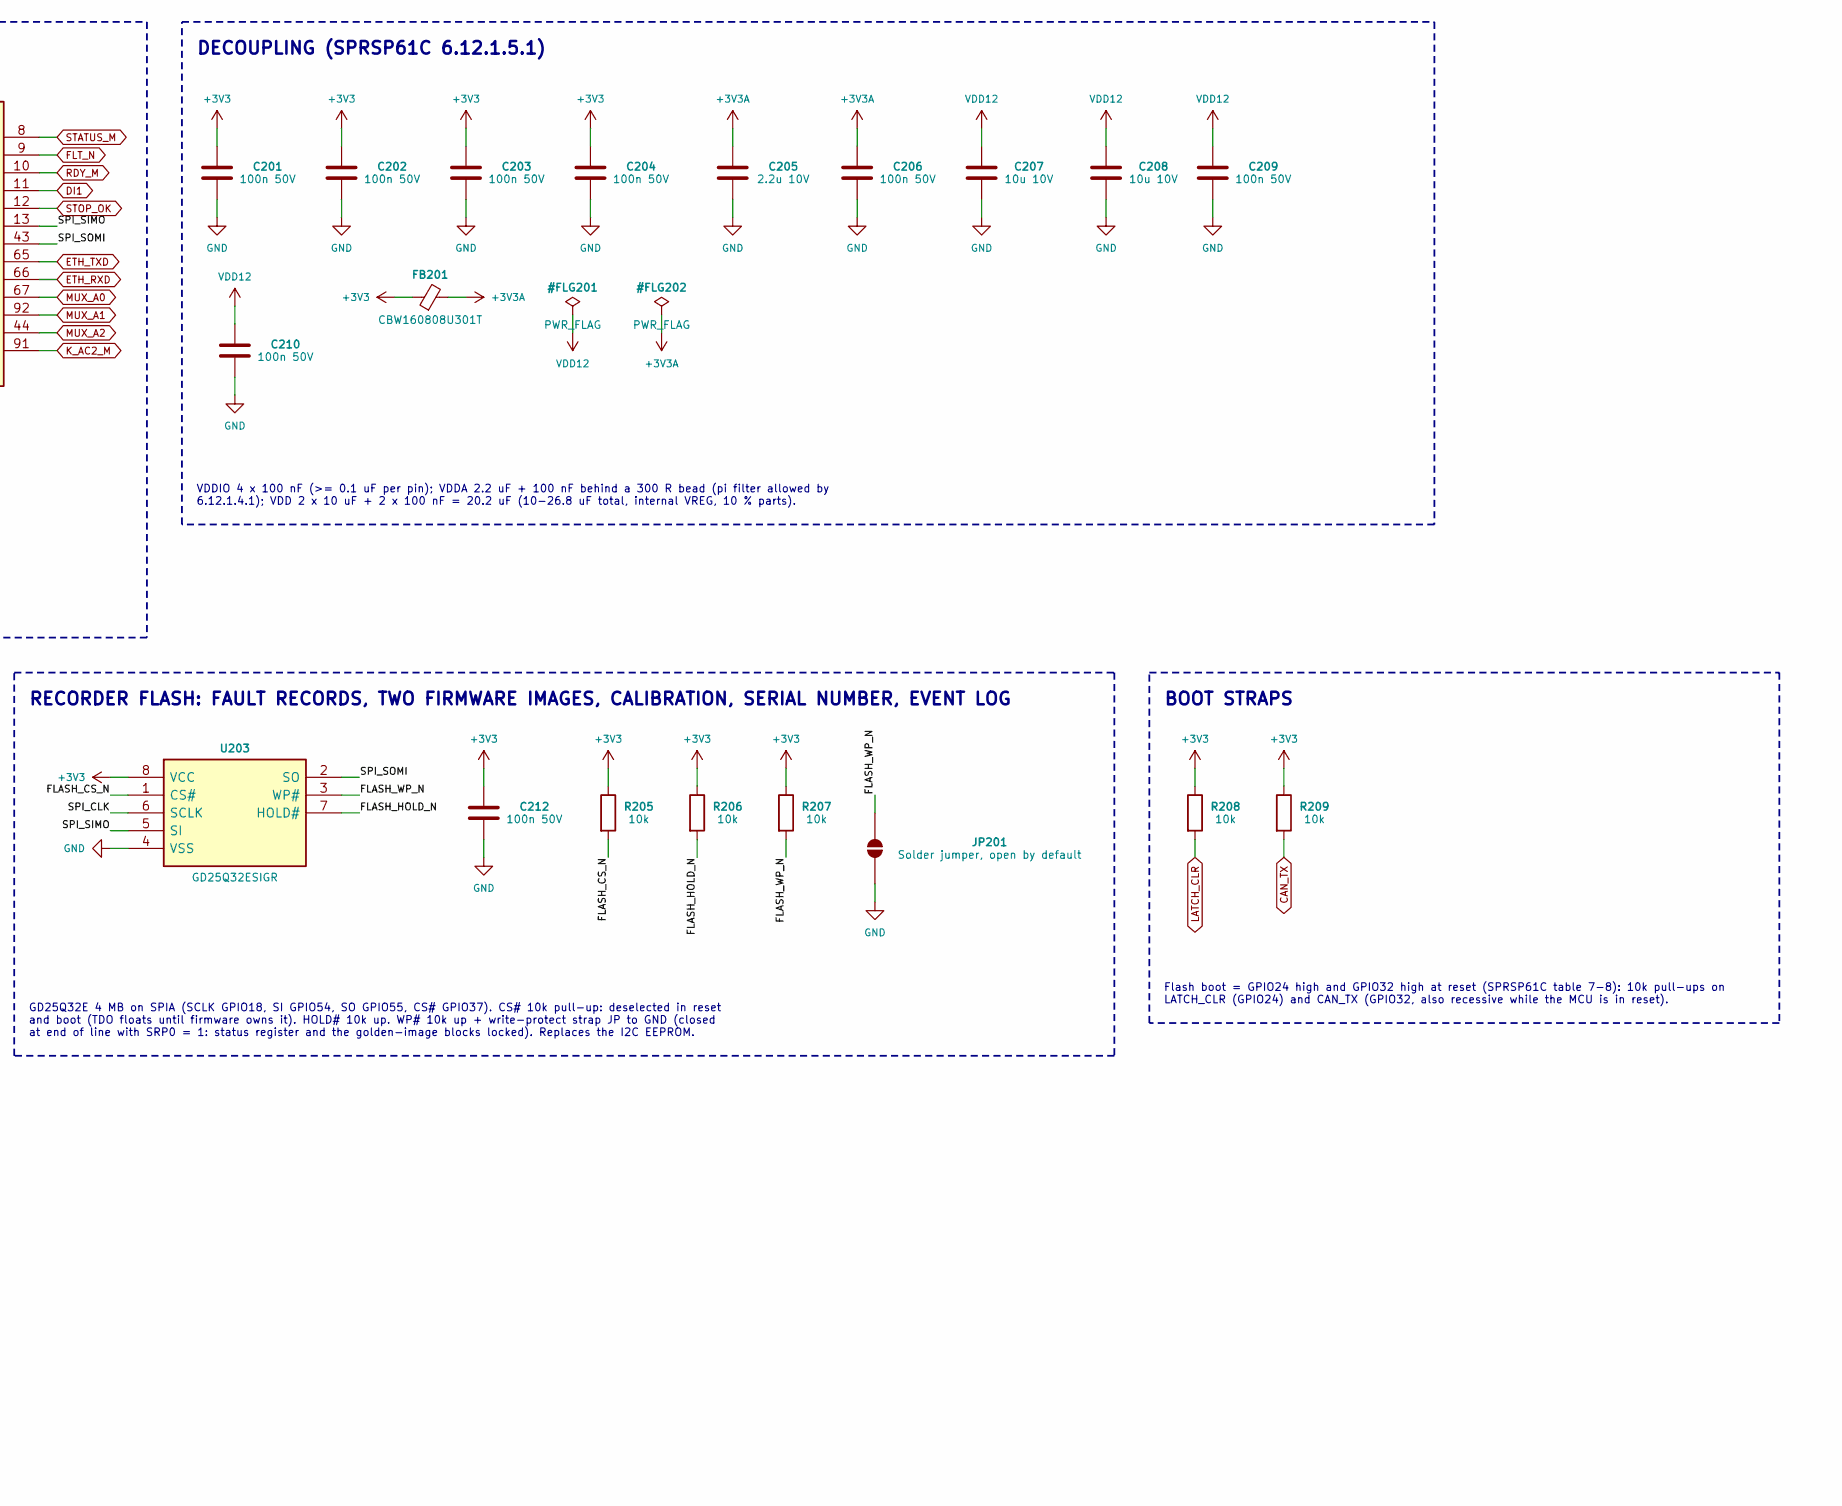
[picture p274: schematic 02_mcu.kicad_sch, part in row 1, column 2]

Parts:
C201, C202, C203, C204, C206, C209, C210, C211, C212: 100n 50V
C205: 2.2u 10V
C207, C208: 10u 10V
D201: 150060VS75000; MPN 150060VS75000
FB201: CBW160808U301T; MPN CBW160808U301T
J201: X1270WVS-2x10B-9TV01; MPN X1270WVS-2x10B-9TV01
JP201: Solder jumper, open by default
R201: 2.2k
R202: 100R
R203, R204: 4.7k
R205, R206, R207, R208, R209: 10k
R210: 680R
RN201, RN202, RN203, RN204, RN205, RN206: 4 x 10k; MPN 4D03WGJ0103T5E
U201: F280039CSPZR; MPN F280039CSPZR
U202: X1G0041710033; MPN X1G0041710033
U203: GD25Q32ESIGR; MPN GD25Q32ESIGR

Connections:
+3V3: C201.1, C202.1, C203.1, C204.1, C211.1, C212.1, FB201.1, R201.1, R202.1, R203.1, R204.1, R205.1, R206.1, R207.1, R208.1, R209.1, U201.3 (VDDIO), U201.47 (VDDIO), U201.70 (VDDIO), U201.88 (VDDIO), U202.1 (~ST), U202.4 (VCC), U203.8 (VCC)
+3V3A: C205.1, C206.1, FB201.2, U201.34 (VDDA)
BIAS_EN: U201.80 (GPIO40)
CAN_RX: U201.53 (GPIO33)
CAN_TX: R209.2, U201.64 (GPIO32)
DI1: U201.11 (GPIO52)
EN_M: RN205.1 (R1.1), U201.99 (GPIO31)
ETH_RXD: U201.66 (GPIO57)
ETH_TXD: U201.65 (GPIO56)
FAN_PWM_M: RN206.2 (R2.1), U201.58 (GPIO26)
FLASH_CS_N: R205.2, U201.61 (GPIO37/TDO), U203.1 (CS#)
FLASH_HOLD_N: R206.2, U203.7 (HOLD#)
FLASH_WP_N: JP201.1 (A), R207.2, U203.3 (WP#)
FLT_N: U201.9 (GPIO50)
GND: C201.2, C202.2, C203.2, C204.2, C205.2, C206.2, C207.2, C208.2, C209.2, C210.2, C211.2, C212.2, D201.1 (K), J201.4, J201.8, J201.10, J201.12, J201.16, J201.17, J201.18, J201.19, J201.20, JP201.2 (B), RN201.5 (R4.2), RN201.6 (R3.2), RN201.7 (R2.2), RN201.8 (R1.2), RN202.5 (R4.2), RN202.6 (R3.2), RN202.7 (R2.2), RN202.8 (R1.2), RN203.5 (R4.2), RN203.6 (R3.2), RN203.7 (R2.2), RN203.8 (R1.2), RN204.5 (R4.2), RN204.6 (R3.2), RN204.7 (R2.2), RN204.8 (R1.2), RN205.5 (R4.2), RN205.6 (R3.2), RN205.7 (R2.2), RN205.8 (R1.2), RN206.5 (R4.2), RN206.6 (R3.2), RN206.7 (R2.2), RN206.8 (R1.2), U201.5 (VSS), U201.26 (VREFLO), U201.27 (VREFLO), U201.33 (VSSA), U201.45 (VSS), U201.72 (VSS), U201.73 (VREGENZ), U201.86 (VSS), U202.2 (GND), U203.4 (VSS)
HEARTBEAT: RN206.3 (R3.1), U201.59 (GPIO27)
HOLD: U201.6 (GPIO47)
IB_ADC: U201.31 (A7/C3)
IB_H_ADC: U201.28 (A12/C5)
IL1_ADC: U201.17 (A2/B6/C9)
IL2_ADC: U201.40 (A10/B1/C10)
IL3_ADC: U201.19 (A14/B14/C4)
IL4_ADC: U201.39 (B4/C8)
IMD_SW1: U201.82 (GPIO41)
IMD_SW2: U201.85 (GPIO44)
JTAG_EMU0: J201.13, R203.2
JTAG_EMU1: J201.14, R204.2
JTAG_VREF: J201.5, R202.2
K_AC2_M: RN206.4 (R4.1), U201.91 (GPIO61)
K_A_M: RN205.2 (R2.1), U201.83 (GPIO22)
K_B_M: RN205.3 (R3.1), U201.81 (GPIO23)
K_PRE_M: RN205.4 (R4.1), U201.57 (GPIO25)
LATCH_CLR: R208.2, U201.56 (GPIO24)
LED_RUN_A: D201.2 (A), R210.2
MOV_OK: U201.7 (GPIO48)
MUX_A0: U201.67 (GPIO58)
MUX_A1: U201.92 (GPIO59)
MUX_A2: U201.44 (GPIO60)
NTC9: U201.38 (A9)
NTC_IN: U201.42 (C14)
NTC_MUX: U201.36 (A4/B8)
OSC_CLK: U201.69 (GPIO19/X1), U202.3 (OUT)
PRE_N: U201.55 (GPIO17)
PWM1_M: RN201.1 (R1.1), U201.79 (GPIO0)
PWM2_M: RN201.2 (R2.1), U201.78 (GPIO1)
PWM3_M: RN201.3 (R3.1), U201.77 (GPIO2)
PWM4_M: RN201.4 (R4.1), U201.76 (GPIO3)
PWM5_M: RN202.1 (R1.1), U201.75 (GPIO4)
PWM6_M: RN202.2 (R2.1), U201.89 (GPIO5)
PWM7_M: RN202.3 (R3.1), U201.97 (GPIO6)
PWM8_M: RN202.4 (R4.1), U201.84 (GPIO7)
PWM9_M: RN203.1 (R1.1), U201.74 (GPIO8)
PWM10_M: RN203.2 (R2.1), U201.90 (GPIO9)
PWM11_M: RN203.3 (R3.1), U201.93 (GPIO10)
PWM12_M: RN203.4 (R4.1), U201.52 (GPIO11)
PWM13_M: RN204.1 (R1.1), U201.51 (GPIO12)
PWM14_M: RN204.2 (R2.1), U201.50 (GPIO13)
PWM15_M: RN204.3 (R3.1), U201.96 (GPIO14)
PWM16_M: RN204.4 (R4.1), U201.95 (GPIO15)
RCM_ADC: U201.37 (A8)
RCM_TST: U201.49 (B11/GPIO21)
RDY_M: U201.10 (GPIO51)
RS485_DE: U201.98 (GPIO30)
SCI_RX: U201.1 (GPIO28)
SCI_TX: U201.100 (GPIO29)
SPI_CLK: U201.68 (GPIO18/X2), U203.6 (SCLK)
SPI_SIMO: U201.13 (GPIO54), U203.5 (SI)
SPI_SOMI: U201.43 (GPIO55), U203.2 (SO)
STATUS_M: RN206.1 (R1.1), U201.8 (GPIO49)
STOP_OK: U201.12 (GPIO53)
TACH1: U201.63 (GPIO35/TDI)
TACH2: U201.94 (GPIO34)
TACH3: U201.48 (B5/GPIO20)
TCK: J201.9, J201.11, U201.60 (TCK)
TMS: J201.1, R201.2, U201.62 (TMS)
TRIP: U201.54 (GPIO16)
VA_ADC: U201.20 (A11/B10/C0)
VBX_ADC: U201.15 (B2/C6)
VB_ADC: U201.22 (A1/B7/DACB_OUT)
VC1_ADC: U201.35 (A5)
VC2_ADC: U201.32 (B5)
VC3_ADC: U201.41 (B0/C11)
VDD12: C207.1, C208.1, C209.1, C210.1, U201.4 (VDD), U201.46 (VDD), U201.71 (VDD), U201.87 (VDD)
VG1_ADC: U201.14 (A6)
VG2_ADC: U201.30 (B11)
VG3_ADC: U201.29 (C1)
VGN_ADC: U201.21 (B12/C2)
VPE_ADC: U201.18 (A3/B9/C7)
VREF: U201.16 (B3/VDAC), U201.24 (VREFHI), U201.25 (VREFHI)
WD_OK: R210.1
XRSn: J201.15, U201.2 (XRSn)

Notes on the sheet:
GD25Q32E 4 MB on SPIA (SCLK GPIO18, SI GPIO54, SO GPIO55, CS# GPIO37). CS# 10k pull-up: deselected in reset and boot (TDO floats until firmware owns it). HOLD# 10k up. WP# 10k up + write-protect strap JP to GND (closed at end of line with SRP0 = 1: status register and the golden-image blocks locked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
RUN LED ON WD_OK (REV A2: GPIO34 FREED; WD_OK FROM SHEET 05)
25 MHZ CLOCK (X1 SINGLE-ENDED)
Every MCU output that ends in an AND gate here is low while the MCU is in reset or unprogrammed (GPIOs high impedance): 16 PWM, EN, K_A, K_B, K_PRE, STATUS, FAN_PWM, HEARTBEAT, K_AC2 (24 lines, 0 spare elements). BIAS_EN, IMD_SW1/2 go straight to PC: pulled down on the power board (10k / 100k, PV-P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
Green, lit while the heartbeat monoflop holds WD_OK high (control ISR running, no MCU reset): the hardware's own view of 'firmware alive'. 680 R, ~2 mA from the 74LVC1G123 output (IOH 24 mA at 3.0 V).
VDDIO 4 x 100 nF (>= 0.1 uF per pin); VDDA 2.2 uF + 100 nF behind a 300 R bead (pi filter allowed by 6.12.1.4.1); VDD 2 x 10 uF + 2 x 100 nF = 20.2 uF (10-26.8 uF total, internal VREG, 10 % parts).
Pins as gen/data/pv_ctrl_pin_plan.csv (checked against SPRSP61C table 5-1 on every build). VREGENZ = GND: internal 1.2 V VREG; VDD only decoupled.
F280039CSPZR
COMMAND PULL-DOWNS (6 X 4 X 10K ARRAYS)
SG-210STF +/-50 ppm (CAN bit timing; CAN boot needs the external clock). f(X1) 10-25 MHz, tr/tf <= 6 ns (SPRSP61C 6.12.3.2.1).
DECOUPLING (SPRSP61C 6.12.1.5.1)
Label: 'HAZARDOUS VOLTAGE - up to 1000 V DC to earth - isolated debug probe only'. cJTAG (IEEE 1149.7, TMS + TCK; SPRSP61C 6.12.6): TDI (3) / TDO (7) open, GPIO35 / 37 are TACH1 / flash CS#. TMS 2.2k pull-up; TRST (2) open; EMU0/1 4.7k; RESET (15) on XRSn. Field update over Ethernet / RS-485 / CAN: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
Flash boot = GPIO24 high and GPIO32 high at reset (SPRSP61C table 7-8): 10k pull-ups on LATCH_CLR (GPIO24) and CAN_TX (GPIO32, also recessive while the MCU is in reset).
BOOT STRAPS
RECORDER FLASH: FAULT RECORDS, TWO FIRMWARE IMAGES, CALIBRATION, SERIAL NUMBER, EVENT LOG
JTAG CTI-20 IN CJTAG MODE - HAZARDOUS LIVE (ISOLATED PROBE ONLY)
