vectivolt/PCM/hardware/PCS-CTL/sheets/05_latch.kicad_sch

## KiCad design hardware/PCS-CTL/sheets/05_latch.kicad_sch (2026-10-06)

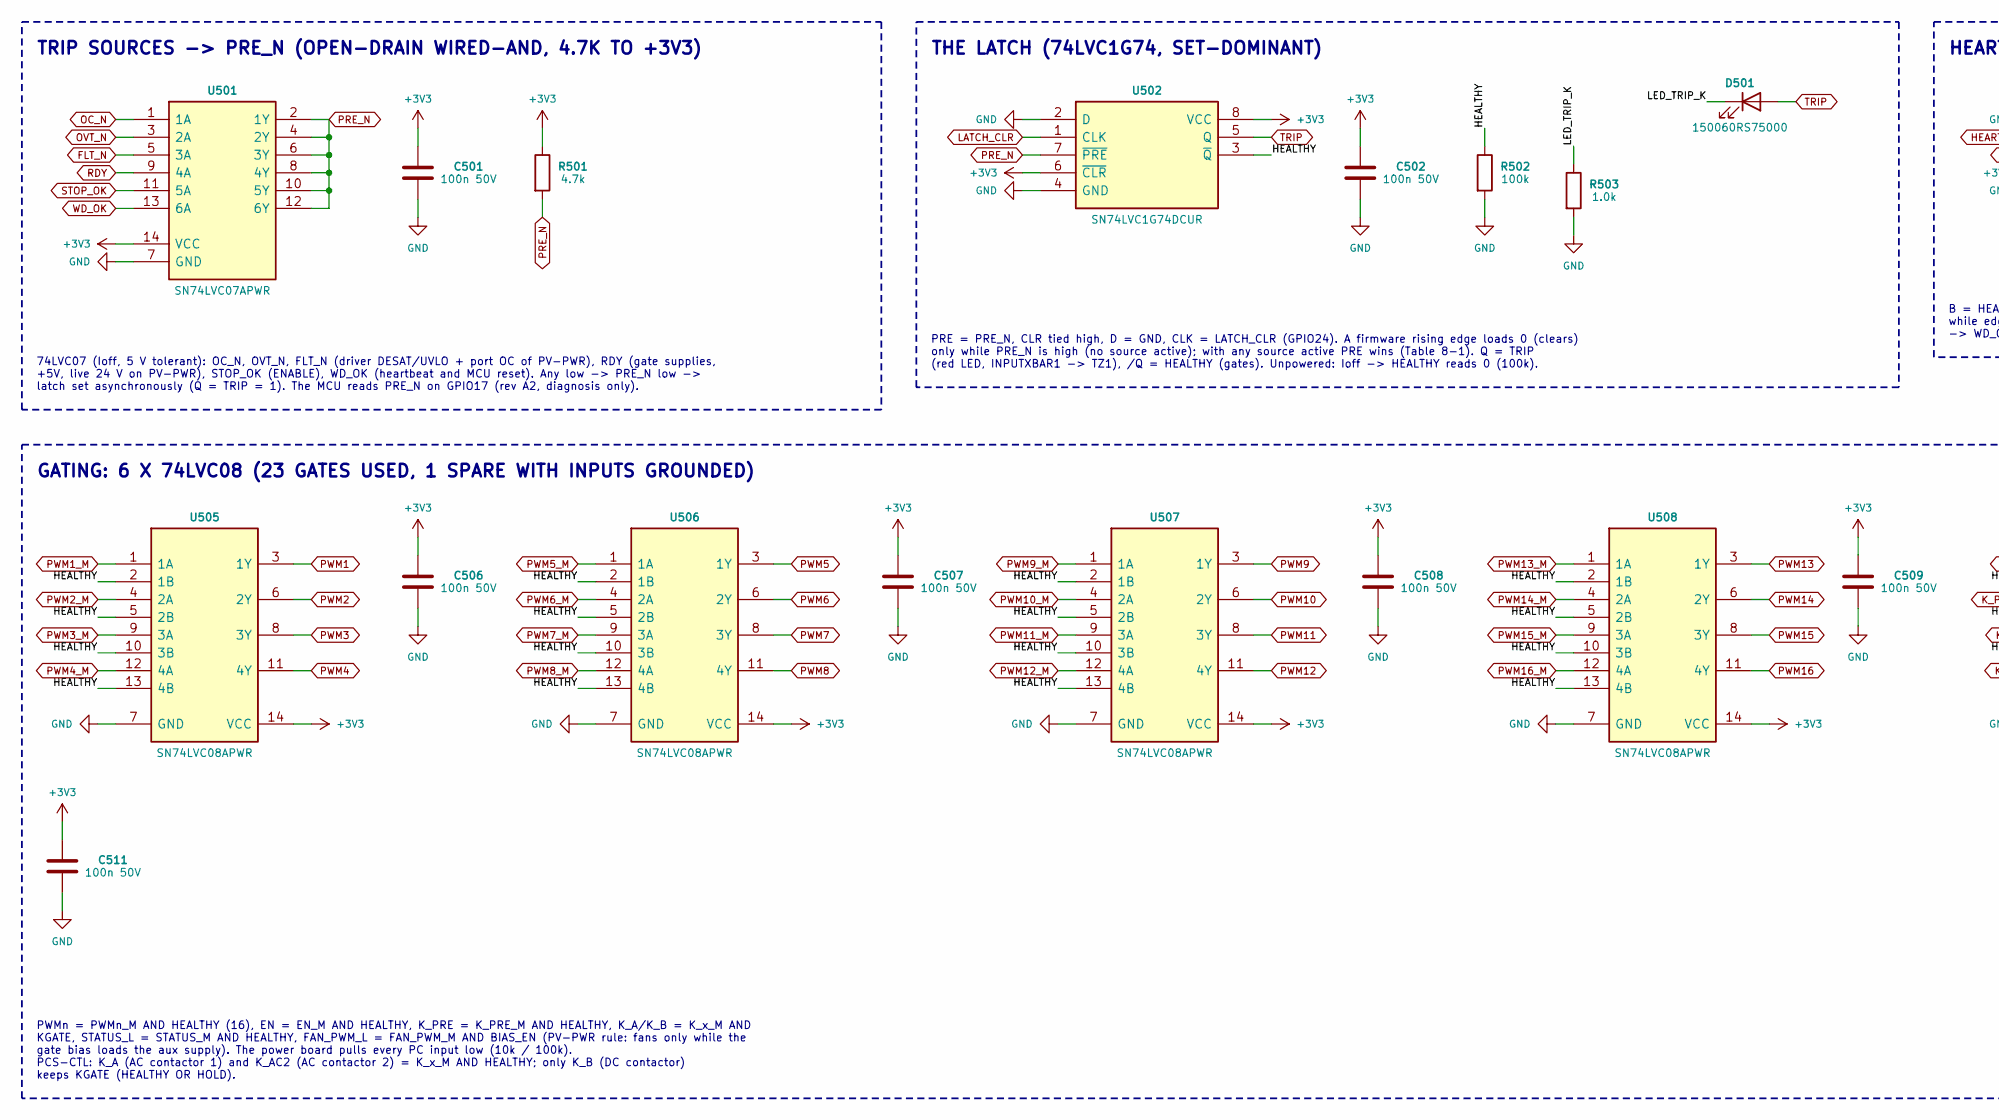
[picture p279: schematic 05_latch.kicad_sch, part in row 1, column 1]

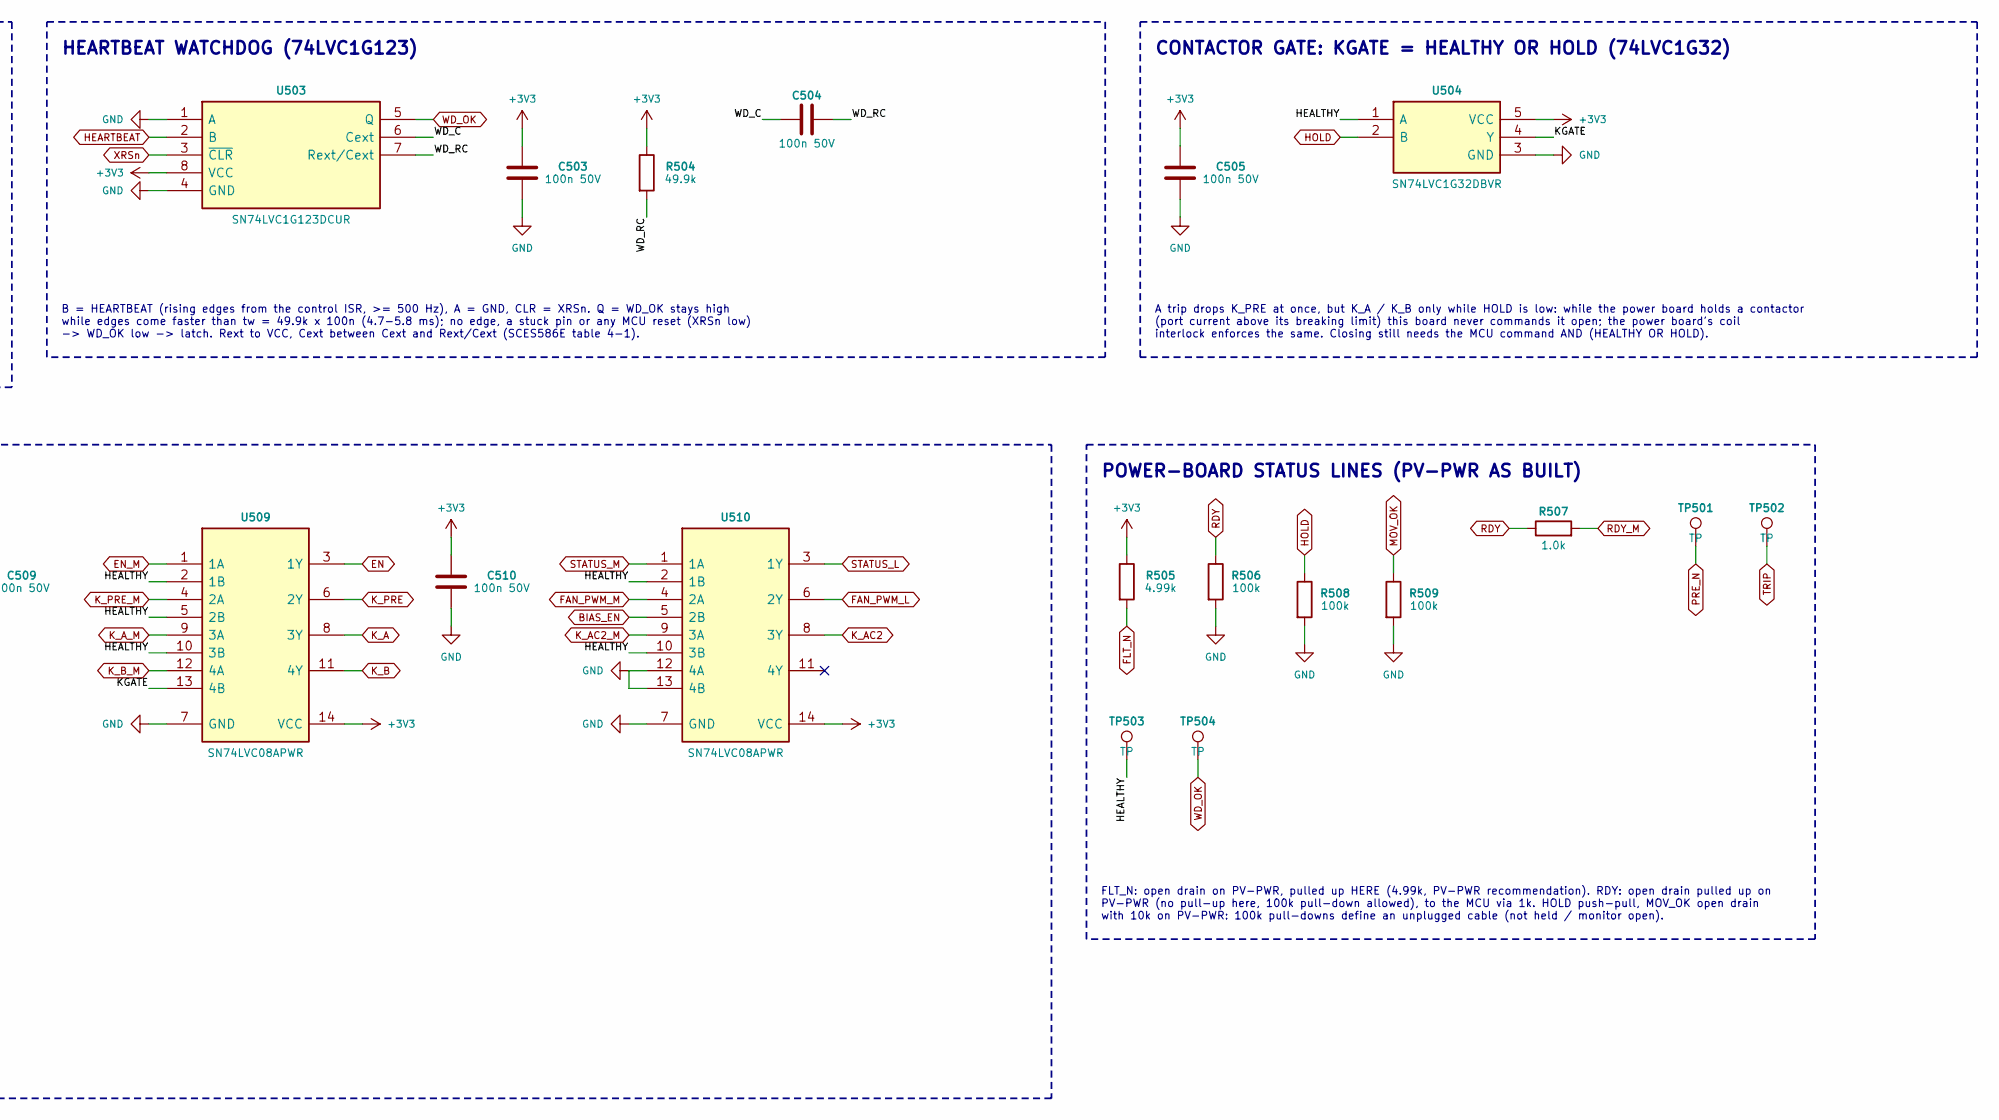
[picture p280: schematic 05_latch.kicad_sch, part in row 1, column 2]

Parts:
C501, C502, C503, C504, C505, C506, C507, C508, C509, C510, C511: 100n 50V
D501: 150060RS75000; MPN 150060RS75000
R501: 4.7k
R502, R506, R508, R509: 100k
R503, R507: 1.0k
R504: 49.9k
R505: 4.99k
TP501, TP502, TP503, TP504: TP
U501: SN74LVC07APWR; MPN SN74LVC07APWR
U502: SN74LVC1G74DCUR; MPN SN74LVC1G74DCUR
U503: SN74LVC1G123DCUR; MPN SN74LVC1G123DCUR
U504: SN74LVC1G32DBVR; MPN SN74LVC1G32DBVR
U505, U506, U507, U508, U509, U510: SN74LVC08APWR; MPN SN74LVC08APWR

Connections:
+3V3: C501.1, C502.1, C503.1, C505.1, C506.1, C507.1, C508.1, C509.1, C510.1, C511.1, R501.1, R504.1, R505.1, U501.14 (VCC), U502.6 (~CLR), U502.8 (VCC), U503.8 (VCC), U504.5 (VCC), U505.14 (VCC), U506.14 (VCC), U507.14 (VCC), U508.14 (VCC), U509.14 (VCC), U510.14 (VCC)
BIAS_EN: U510.5 (2B)
EN: U509.3 (1Y)
EN_M: U509.1 (1A)
FAN_PWM_L: U510.6 (2Y)
FAN_PWM_M: U510.4 (2A)
FLT_N: R505.2, U501.5 (3A)
GND: C501.2, C502.2, C503.2, C505.2, C506.2, C507.2, C508.2, C509.2, C510.2, C511.2, R502.2, R503.2, R506.2, R508.2, R509.2, U501.7 (GND), U502.2 (D), U502.4 (GND), U503.1 (A), U503.4 (GND), U504.3 (GND), U505.7 (GND), U506.7 (GND), U507.7 (GND), U508.7 (GND), U509.7 (GND), U510.7 (GND), U510.12 (4A), U510.13 (4B)
HEALTHY: R502.1, TP503.1, U502.3 (~Q), U504.1 (A), U505.2 (1B), U505.5 (2B), U505.10 (3B), U505.13 (4B), U506.2 (1B), U506.5 (2B), U506.10 (3B), U506.13 (4B), U507.2 (1B), U507.5 (2B), U507.10 (3B), U507.13 (4B), U508.2 (1B), U508.5 (2B), U508.10 (3B), U508.13 (4B), U509.2 (1B), U509.5 (2B), U509.10 (3B), U510.2 (1B), U510.10 (3B)
HEARTBEAT: U503.2 (B)
HOLD: R508.1, U504.2 (B)
KGATE: U504.4 (Y), U509.13 (4B)
K_A: U509.8 (3Y)
K_AC2: U510.8 (3Y)
K_AC2_M: U510.9 (3A)
K_A_M: U509.9 (3A)
K_B: U509.11 (4Y)
K_B_M: U509.12 (4A)
K_PRE: U509.6 (2Y)
K_PRE_M: U509.4 (2A)
LATCH_CLR: U502.1 (CLK)
LED_TRIP_K: D501.1 (K), R503.1
MOV_OK: R509.1
OC_N: U501.1 (1A)
OVT_N: U501.3 (2A)
PRE_N: R501.2, TP501.1, U501.2 (1Y), U501.4 (2Y), U501.6 (3Y), U501.8 (4Y), U501.10 (5Y), U501.12 (6Y), U502.7 (~PRE)
PWM1: U505.3 (1Y)
PWM1_M: U505.1 (1A)
PWM2: U505.6 (2Y)
PWM2_M: U505.4 (2A)
PWM3: U505.8 (3Y)
PWM3_M: U505.9 (3A)
PWM4: U505.11 (4Y)
PWM4_M: U505.12 (4A)
PWM5: U506.3 (1Y)
PWM5_M: U506.1 (1A)
PWM6: U506.6 (2Y)
PWM6_M: U506.4 (2A)
PWM7: U506.8 (3Y)
PWM7_M: U506.9 (3A)
PWM8: U506.11 (4Y)
PWM8_M: U506.12 (4A)
PWM9: U507.3 (1Y)
PWM9_M: U507.1 (1A)
PWM10: U507.6 (2Y)
PWM10_M: U507.4 (2A)
PWM11: U507.8 (3Y)
PWM11_M: U507.9 (3A)
PWM12: U507.11 (4Y)
PWM12_M: U507.12 (4A)
PWM13: U508.3 (1Y)
PWM13_M: U508.1 (1A)
PWM14: U508.6 (2Y)
PWM14_M: U508.4 (2A)
PWM15: U508.8 (3Y)
PWM15_M: U508.9 (3A)
PWM16: U508.11 (4Y)
PWM16_M: U508.12 (4A)
RDY: R506.1, R507.1, U501.9 (4A)
RDY_M: R507.2
STATUS_L: U510.3 (1Y)
STATUS_M: U510.1 (1A)
STOP_OK: U501.11 (5A)
TRIP: D501.2 (A), TP502.1, U502.5 (Q)
WD_C: C504.1, U503.6 (Cext)
WD_OK: TP504.1, U501.13 (6A), U503.5 (Q)
WD_RC: C504.2, R504.2, U503.7 (Rext/Cext)
XRSn: U503.3 (~CLR)

Notes on the sheet:
74LVC07 (Ioff, 5 V tolerant): OC_N, OVT_N, FLT_N (driver DESAT/UVLO + port OC of PV-PWR), RDY (gate supplies, +5V, live 24 V on PV-PWR), STOP_OK (ENABLE), WD_OK (heartbeat and MCU reset). Any low -> PRE_N low -> latch set asynchronously (Q = TRIP = 1). The MCU reads PRE_N on GPIO17 (rev A2, diagnos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
B = HEARTBEAT (rising edges from the control ISR, >= 500 Hz), A = GND, CLR = XRSn. Q = WD_OK stays high while edges come faster than tw = 49.9k x 100n (4.7-5.8 ms); no edge, a stuck pin or any MCU reset (XRSn low) -> WD_OK low -> latch. Rext to VCC, Cext between Cext and Rext/Cext (SCES586E table 4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
CONTACTOR GATE: KGATE = HEALTHY OR HOLD (74LVC1G32)
PRE = PRE_N, CLR tied high, D = GND, CLK = LATCH_CLR (GPIO24). A firmware rising edge loads 0 (clears) only while PRE_N is high (no source active); with any source active PRE wins (Table 8-1). Q = TRIP (red LED, INPUTXBAR1 -> TZ1), /Q = HEALTHY (gates). Unpowered: Ioff -> HEALTHY reads 0 (100k).
POWER-BOARD STATUS LINES (PV-PWR AS BUILT)
THE LATCH (74LVC1G74, SET-DOMINANT)
GATING: 6 X 74LVC08 (23 GATES USED, 1 SPARE WITH INPUTS GROUNDED)
TRIP SOURCES -> PRE_N (OPEN-DRAIN WIRED-AND, 4.7K TO +3V3)
FLT_N: open drain on PV-PWR, pulled up HERE (4.99k, PV-PWR recommendation). RDY: open drain pulled up on PV-PWR (no pull-up here, 100k pull-down allowed), to the MCU via 1k. HOLD push-pull, MOV_OK open drain with 10k on PV-PWR: 100k pull-downs define an unplugged cable (not held / monitor open).
HEARTBEAT WATCHDOG (74LVC1G123)
A trip drops K_PRE at once, but K_A / K_B only while HOLD is low: while the power board holds a contactor (port current above its breaking limit) this board never commands it open; the power board's coil interlock enforces the same. Closing still needs the MCU command AND (HEALTHY OR HOLD).
PWMn = PWMn_M AND HEALTHY (16), EN = EN_M AND HEALTHY, K_PRE = K_PRE_M AND HEALTHY, K_A/K_B = K_x_M AND KGATE, STATUS_L = STATUS_M AND HEALTHY, FAN_PWM_L = FAN_PWM_M AND BIAS_EN (PV-PWR rule: fans only while the gate bias loads the aux supply). The power board pulls every PC input low (10k / 100k).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
