vectivolt/PCM/hardware/PCS-CTL/sheets/06_iso.kicad_sch

## KiCad design hardware/PCS-CTL/sheets/06_iso.kicad_sch (2026-10-06)

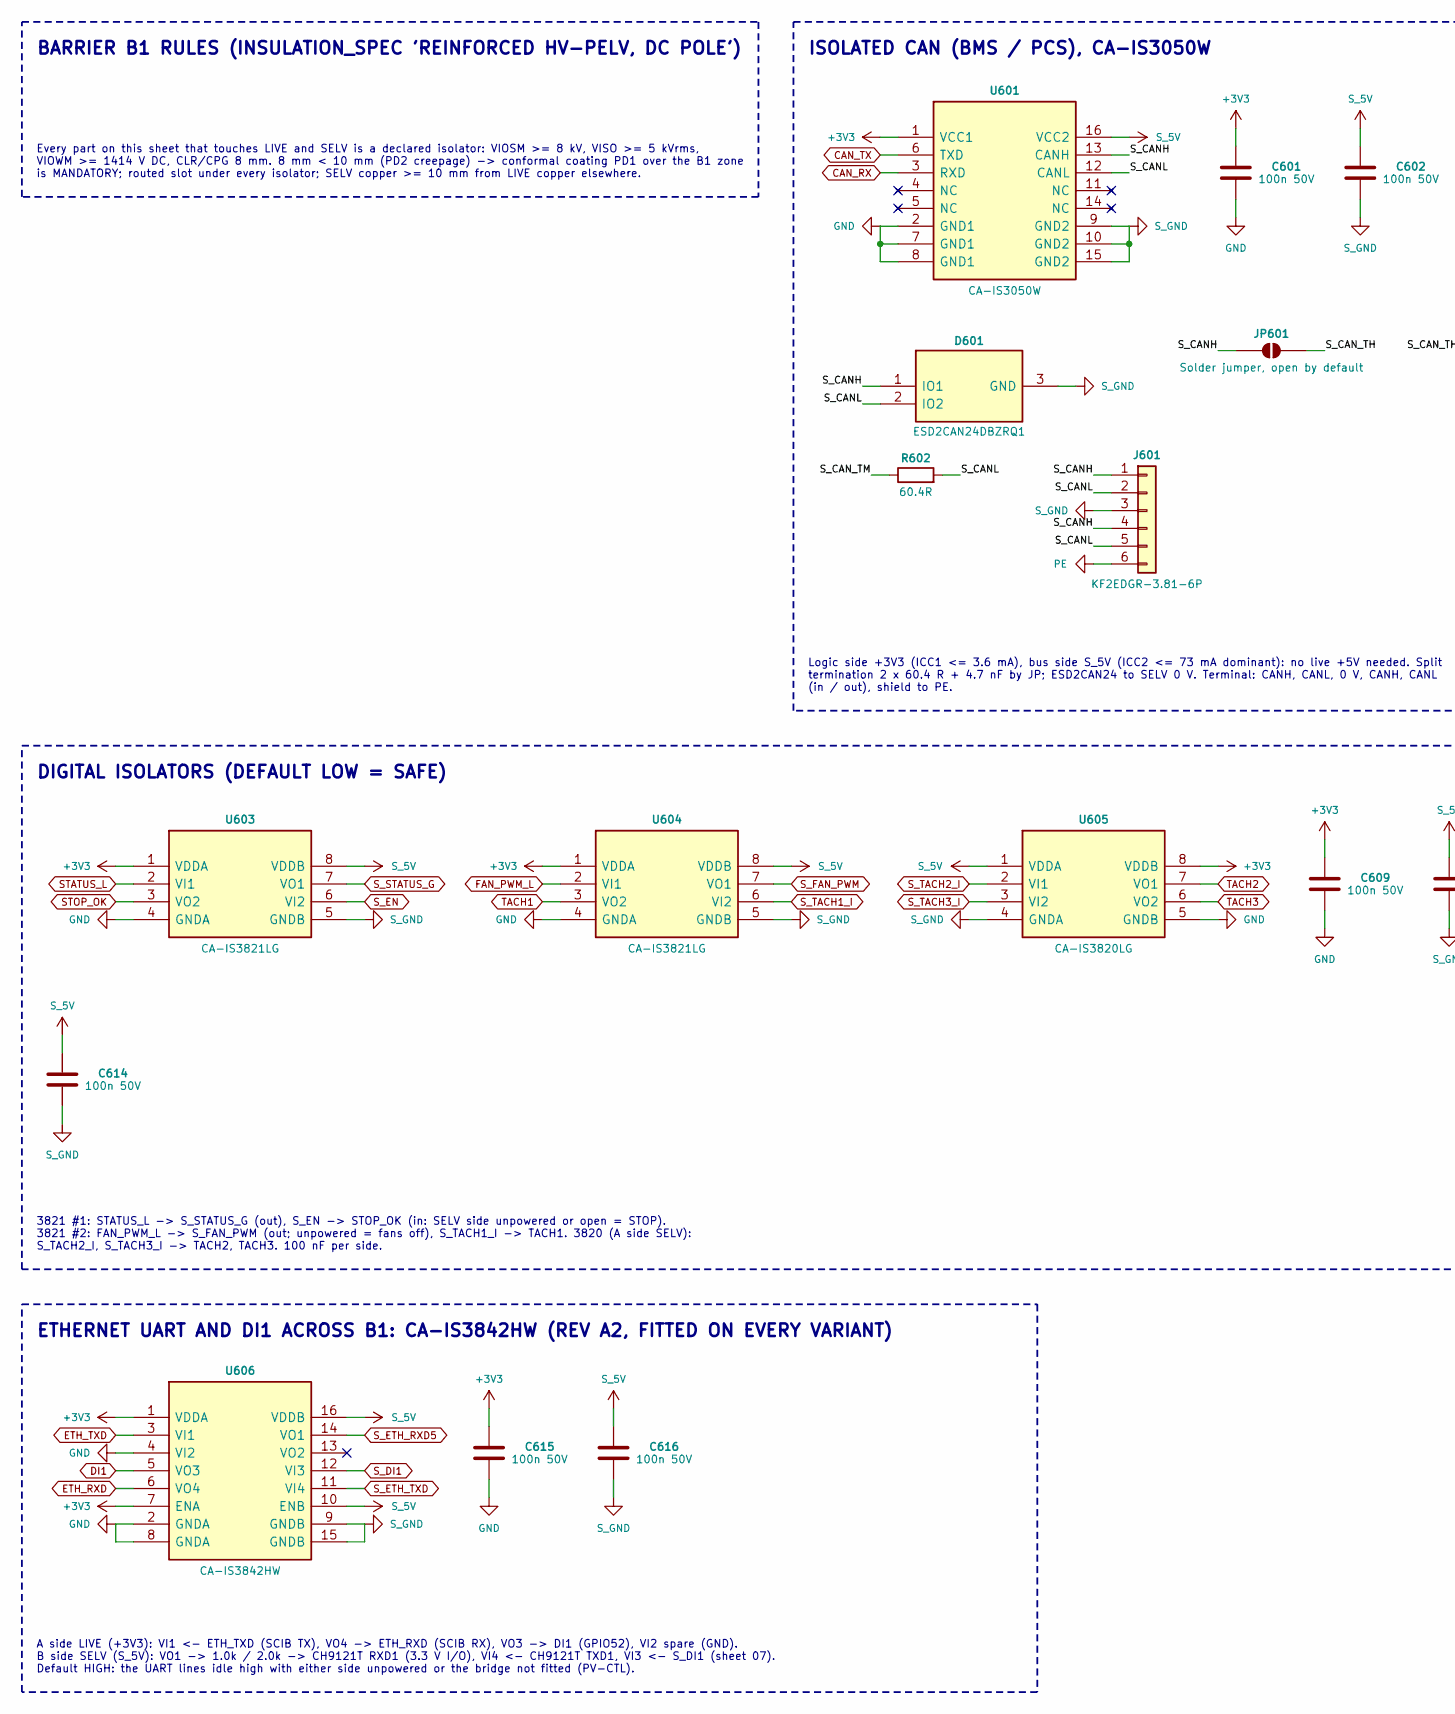
[picture p281: schematic 06_iso.kicad_sch, part in row 1, column 1]

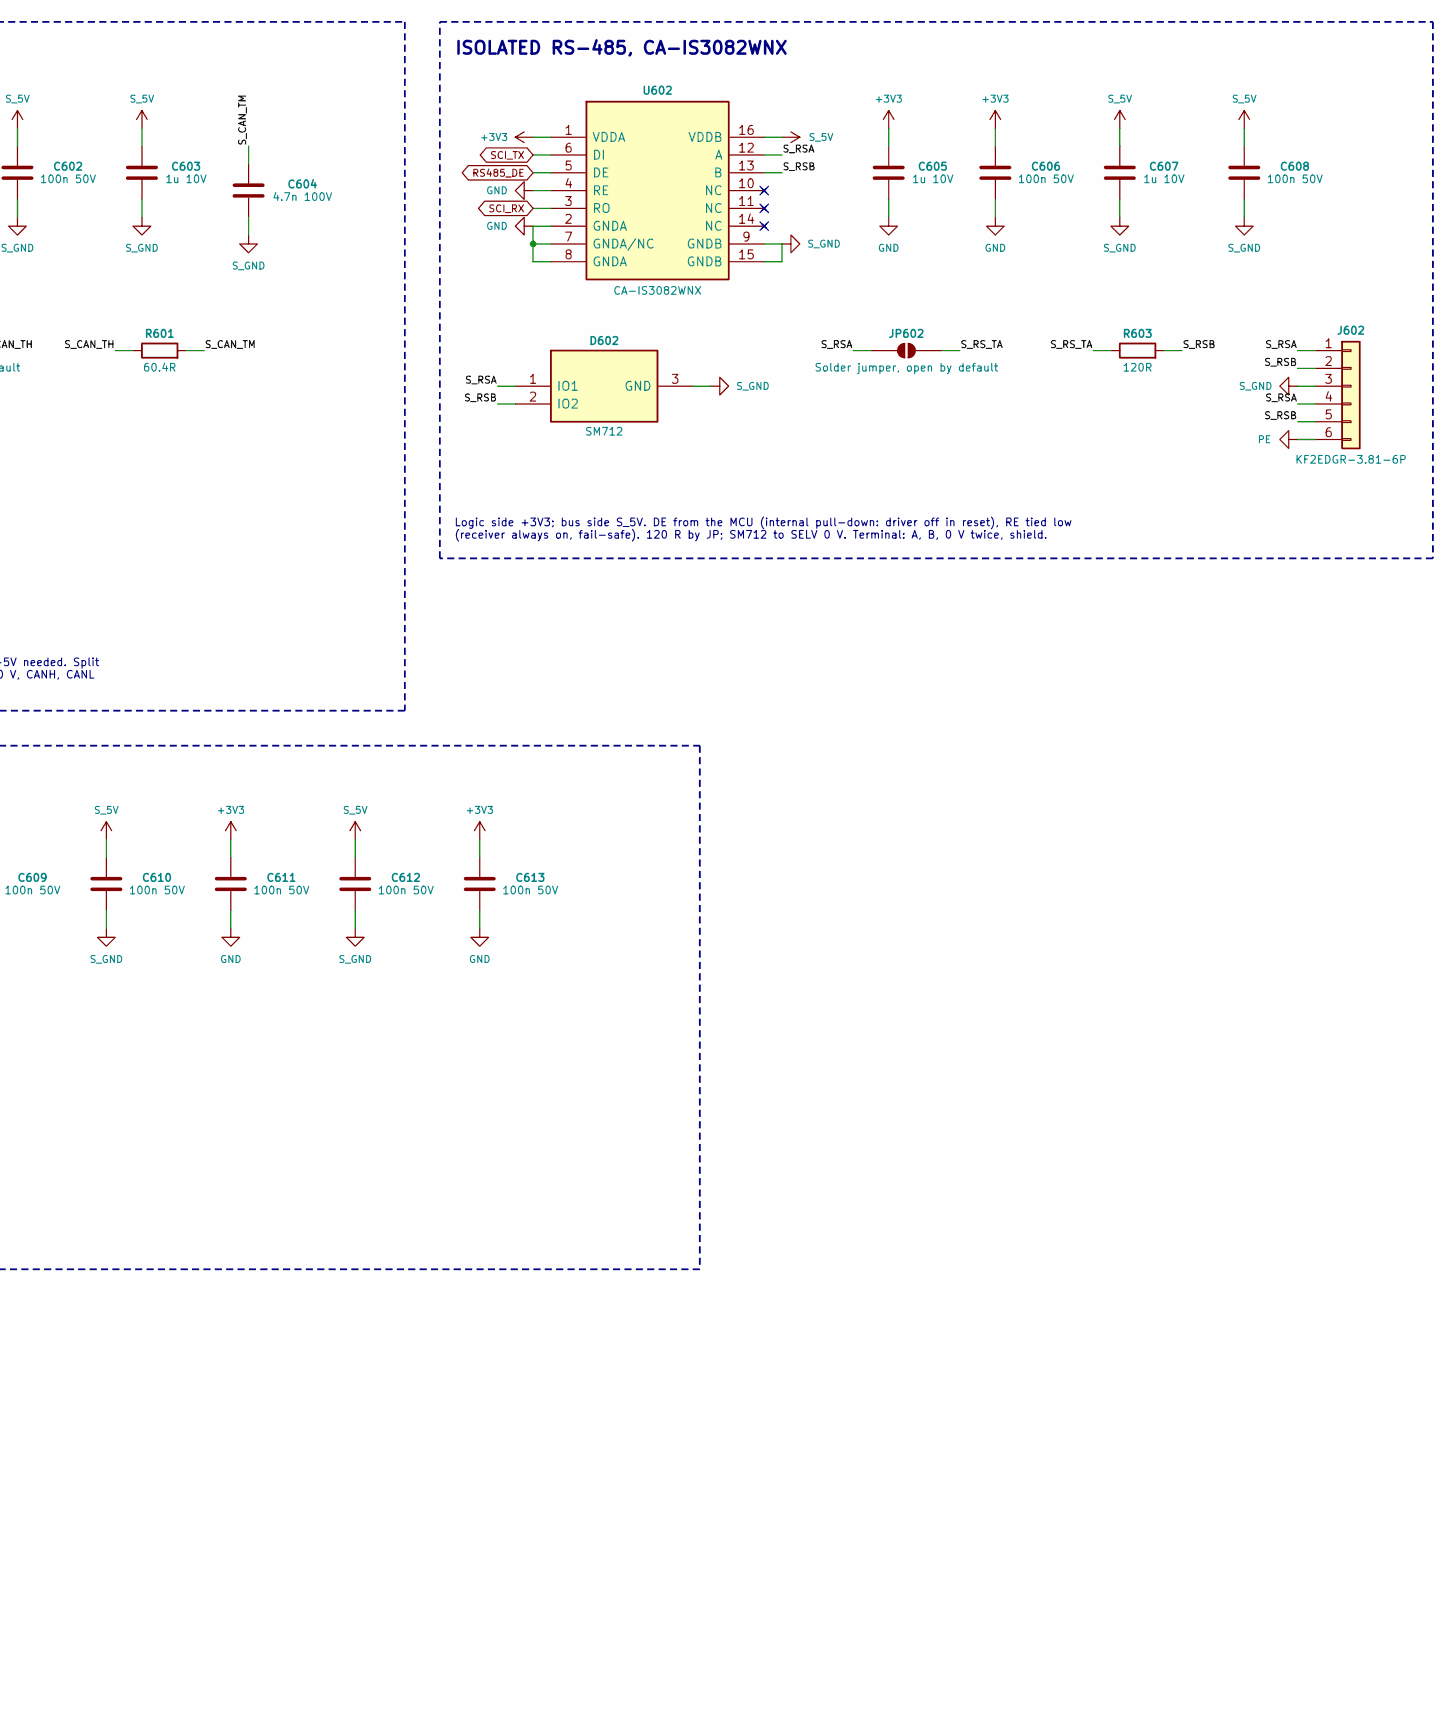
[picture p282: schematic 06_iso.kicad_sch, part in row 1, column 2]

Parts:
C601, C602, C606, C608, C609, C610, C611, C612, C613, C614, C615, C616: 100n 50V
C603, C605, C607: 1u 10V
C604: 4.7n 100V
D601: ESD2CAN24DBZRQ1; MPN ESD2CAN24DBZRQ1
D602: SM712; MPN SM712
J601, J602: KF2EDGR-3.81-6P; MPN KF2EDGR-3.81-6P
JP601, JP602: Solder jumper, open by default
R601, R602: 60.4R
R603: 120R
U601: CA-IS3050W; MPN CA-IS3050W
U602: CA-IS3082WNX; MPN CA-IS3082WNX
U603, U604: CA-IS3821LG; MPN CA-IS3821LG
U605: CA-IS3820LG; MPN CA-IS3820LG
U606: CA-IS3842HW; MPN CA-IS3842HW

Connections:
+3V3: C601.1, C605.1, C606.1, C609.1, C611.1, C613.1, C615.1, U601.1 (VCC1), U602.1 (VDDA), U603.1 (VDDA), U604.1 (VDDA), U605.8 (VDDB), U606.1 (VDDA), U606.7 (ENA)
CAN_RX: U601.3 (RXD)
CAN_TX: U601.6 (TXD)
DI1: U606.5 (VO3)
ETH_RXD: U606.6 (VO4)
ETH_TXD: U606.3 (VI1)
FAN_PWM_L: U604.2 (VI1)
GND: C601.2, C605.2, C606.2, C609.2, C611.2, C613.2, C615.2, U601.2 (GND1), U601.7 (GND1), U601.8 (GND1), U602.2 (GNDA), U602.4 (RE), U602.7 (GNDA/NC), U602.8 (GNDA), U603.4 (GNDA), U604.4 (GNDA), U605.5 (GNDB), U606.2 (GNDA), U606.4 (VI2), U606.8 (GNDA)
PE: J601.6, J602.6
RS485_DE: U602.5 (DE)
SCI_RX: U602.3 (RO)
SCI_TX: U602.6 (DI)
STATUS_L: U603.2 (VI1)
STOP_OK: U603.3 (VO2)
S_5V: C602.1, C603.1, C607.1, C608.1, C610.1, C612.1, C614.1, C616.1, U601.16 (VCC2), U602.16 (VDDB), U603.8 (VDDB), U604.8 (VDDB), U605.1 (VDDA), U606.10 (ENB), U606.16 (VDDB)
S_CANH: D601.1 (IO1), J601.1, J601.4, JP601.1 (A), U601.13 (CANH)
S_CANL: D601.2 (IO2), J601.2, J601.5, R602.2, U601.12 (CANL)
S_CAN_TH: JP601.2 (B), R601.1
S_CAN_TM: C604.1, R601.2, R602.1
S_DI1: U606.12 (VI3)
S_EN: U603.6 (VI2)
S_ETH_RXD5: U606.14 (VO1)
S_ETH_TXD: U606.11 (VI4)
S_FAN_PWM: U604.7 (VO1)
S_GND: C602.2, C603.2, C604.2, C607.2, C608.2, C610.2, C612.2, C614.2, C616.2, D601.3 (GND), D602.3 (GND), J601.3, J602.3, U601.9 (GND2), U601.10 (GND2), U601.15 (GND2), U602.9 (GNDB), U602.15 (GNDB), U603.5 (GNDB), U604.5 (GNDB), U605.4 (GNDA), U606.9 (GNDB), U606.15 (GNDB)
S_RSA: D602.1 (IO1), J602.1, J602.4, JP602.1 (A), U602.12 (A)
S_RSB: D602.2 (IO2), J602.2, J602.5, R603.2, U602.13 (B)
S_RS_TA: JP602.2 (B), R603.1
S_STATUS_G: U603.7 (VO1)
S_TACH1_I: U604.6 (VI2)
S_TACH2_I: U605.2 (VI1)
S_TACH3_I: U605.3 (VI2)
TACH1: U604.3 (VO2)
TACH2: U605.7 (VO1)
TACH3: U605.6 (VO2)

Notes on the sheet:
3821 #1: STATUS_L -> S_STATUS_G (out), S_EN -> STOP_OK (in: SELV side unpowered or open = STOP). 3821 #2: FAN_PWM_L -> S_FAN_PWM (out; unpowered = fans off), S_TACH1_I -> TACH1. 3820 (A side SELV): S_TACH2_I, S_TACH3_I -> TACH2, TACH3. 100 nF per side.
DIGITAL ISOLATORS (DEFAULT LOW = SAFE)
Every part on this sheet that touches LIVE and SELV is a declared isolator: VIOSM >= 8 kV, VISO >= 5 kVrms, VIOWM >= 1414 V DC, CLR/CPG 8 mm. 8 mm < 10 mm (PD2 creepage) -> conformal coating PD1 over the B1 zone is MANDATORY; routed slot under every isolator; SELV copper >= 10 mm from LIVE copper e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
BARRIER B1 RULES (INSULATION_SPEC 'REINFORCED HV-PELV, DC POLE')
ETHERNET UART AND DI1 ACROSS B1: CA-IS3842HW (REV A2, FITTED ON EVERY VARIANT)
Logic side +3V3 (ICC1 <= 3.6 mA), bus side S_5V (ICC2 <= 73 mA dominant): no live +5V needed. Split termination 2 x 60.4 R + 4.7 nF by JP; ESD2CAN24 to SELV 0 V. Terminal: CANH, CANL, 0 V, CANH, CANL (in / out), shield to PE.
ISOLATED RS-485, CA-IS3082WNX
ISOLATED CAN (BMS / PCS), CA-IS3050W
Logic side +3V3; bus side S_5V. DE from the MCU (internal pull-down: driver off in reset), RE tied low (receiver always on, fail-safe). 120 R by JP; SM712 to SELV 0 V. Terminal: A, B, 0 V twice, shield.
A side LIVE (+3V3): VI1 <- ETH_TXD (SCIB TX), VO4 -> ETH_RXD (SCIB RX), VO3 -> DI1 (GPIO52), VI2 spare (GND). B side SELV (S_5V): VO1 -> 1.0k / 2.0k -> CH9121T RXD1 (3.3 V I/O), VI4 <- CH9121T TXD1, VI3 <- S_DI1 (sheet 07). Default HIGH: the UART lines idle high with either side unpowered or the br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
