vectivolt/PCM/hardware/PCS-CTL/sheets/07_selv.kicad_sch

## KiCad design hardware/PCS-CTL/sheets/07_selv.kicad_sch (2026-10-06)

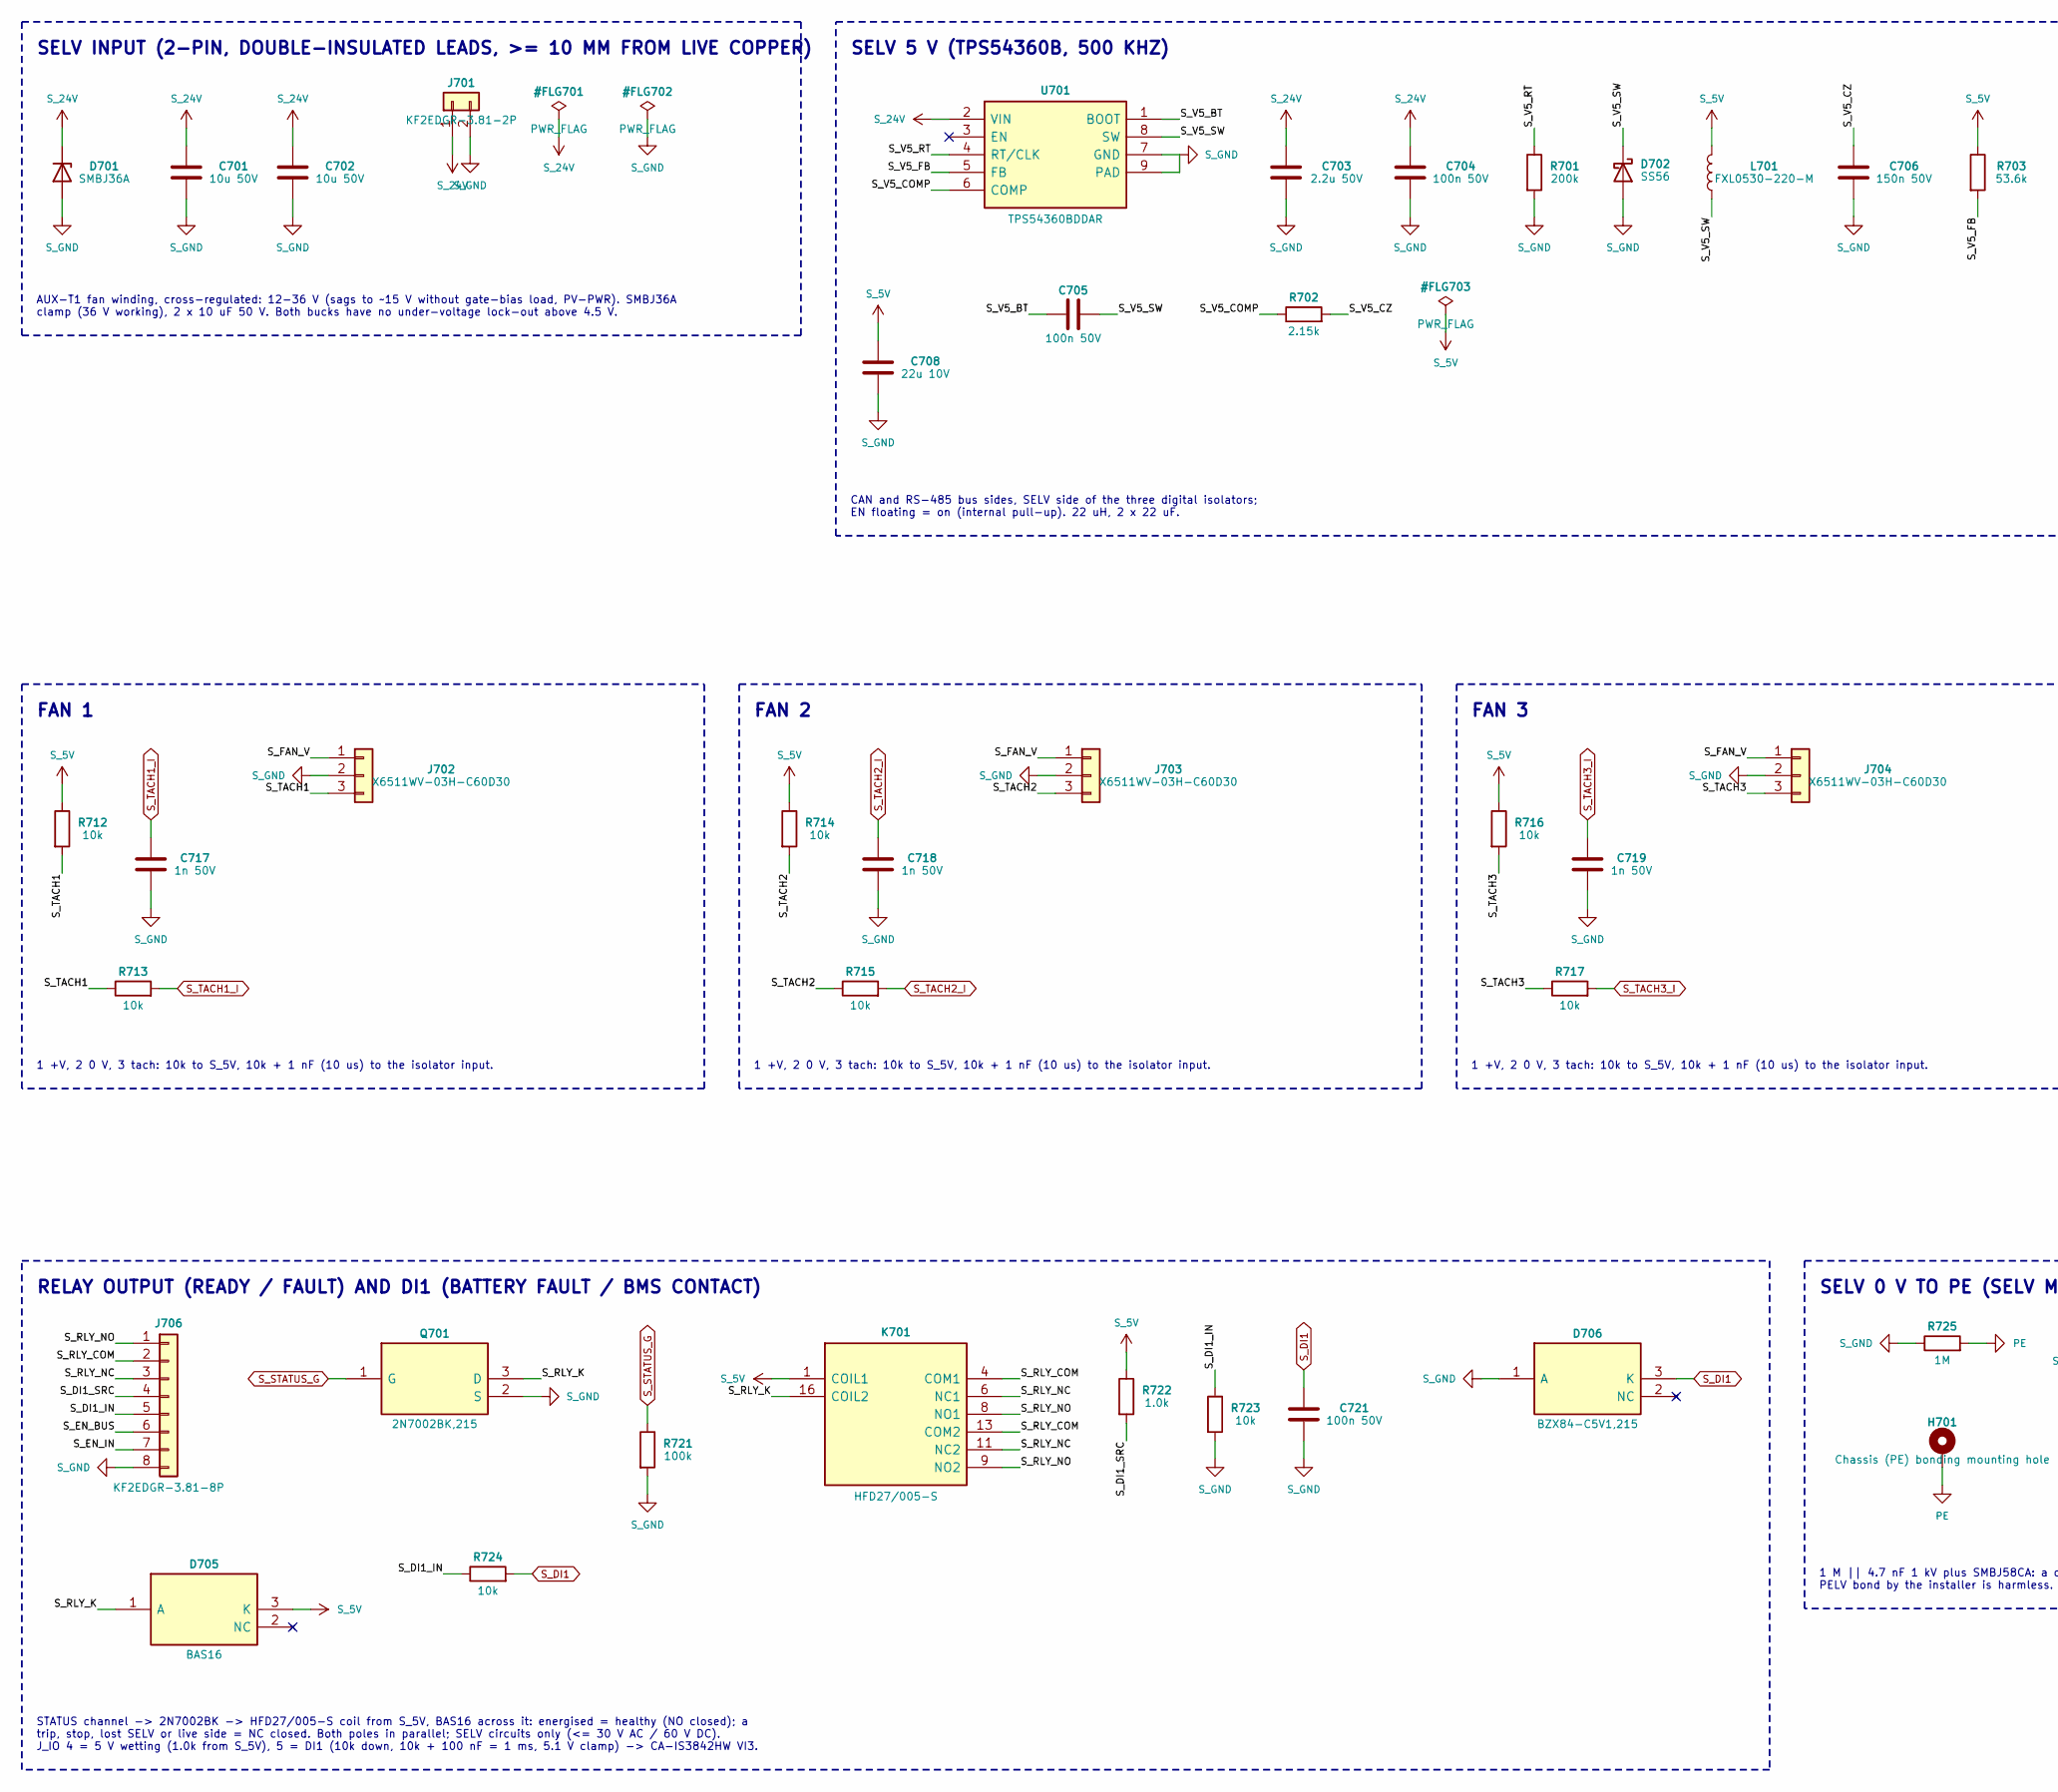
[picture p283: schematic 07_selv.kicad_sch, part in row 1, column 1]

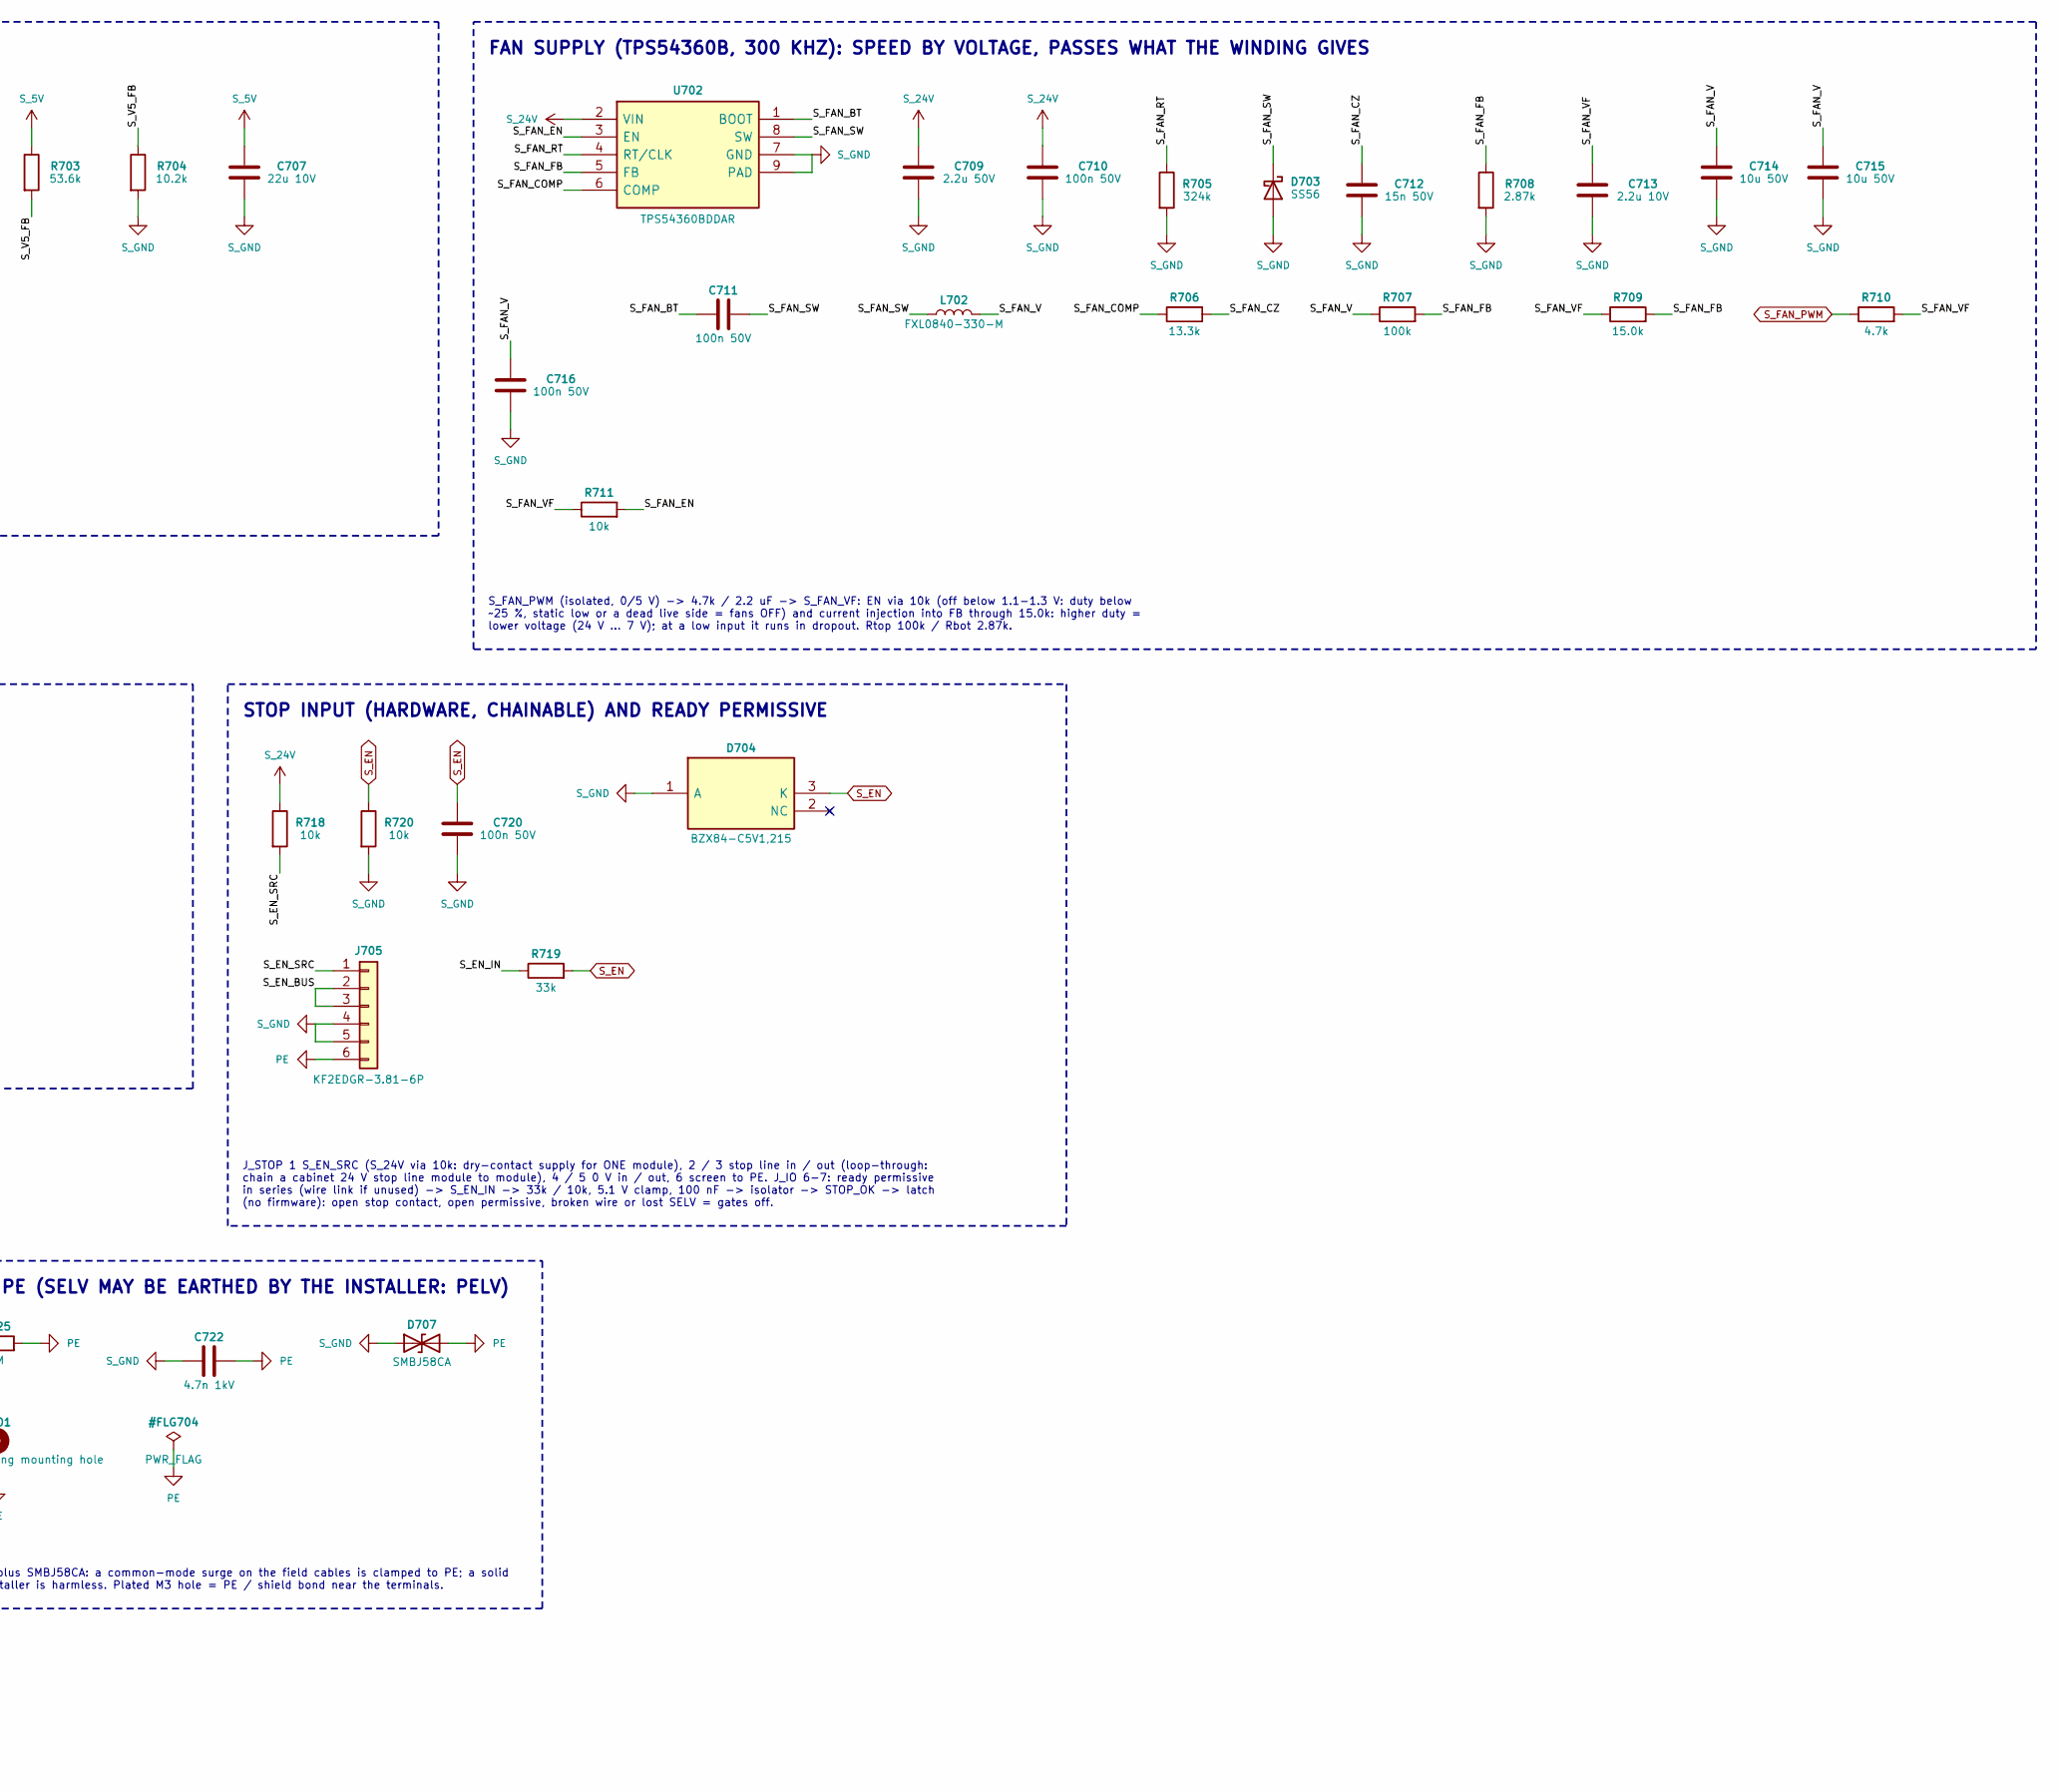
[picture p284: schematic 07_selv.kicad_sch, part in row 1, column 2]

Parts:
C701, C702, C714, C715: 10u 50V
C703, C709: 2.2u 50V
C704, C705, C710, C711, C716, C720, C721: 100n 50V
C706: 150n 50V
C707, C708: 22u 10V
C712: 15n 50V
C713: 2.2u 10V
C717, C718, C719: 1n 50V
C722: 4.7n 1kV
D701: SMBJ36A; MPN SMBJ36A
D702, D703: SS56; MPN SS56
D704, D706: BZX84-C5V1,215; MPN BZX84-C5V1,215
D705: BAS16; MPN BAS16
D707: SMBJ58CA; MPN SMBJ58CA
H701: Chassis (PE) bonding mounting hole
J701: KF2EDGR-3.81-2P; MPN KF2EDGR-3.81-2P
J702, J703, J704: X6511WV-03H-C60D30; MPN X6511WV-03H-C60D30
J705: KF2EDGR-3.81-6P; MPN KF2EDGR-3.81-6P
J706: KF2EDGR-3.81-8P; MPN KF2EDGR-3.81-8P
K701: HFD27/005-S; MPN HFD27/005-S
L701: FXL0530-220-M; MPN FXL0530-220-M
L702: FXL0840-330-M; MPN FXL0840-330-M
Q701: 2N7002BK,215; MPN 2N7002BK,215
R701: 200k
R702: 2.15k
R703: 53.6k
R704: 10.2k
R705: 324k
R706: 13.3k
R707, R721: 100k
R708: 2.87k
R709: 15.0k
R710: 4.7k
R711, R712, R713, R714, R715, R716, R717, R718, R720, R723, R724: 10k
R719: 33k
R722: 1.0k
R725: 1M
U701, U702: TPS54360BDDAR; MPN TPS54360BDDAR

Connections:
PE: C722.2, D707.2 (A2), H701.1, J705.6, R725.2
S_5V: C707.1, C708.1, D705.3 (K), K701.1 (COIL1), L701.2, R703.1, R712.1, R714.1, R716.1, R722.1
S_24V: C701.1, C702.1, C703.1, C704.1, C709.1, C710.1, D701.1 (K), J701.1, R718.1, U701.2 (VIN), U702.2 (VIN)
S_DI1: C721.1, D706.3 (K), R724.2
S_DI1_IN: J706.5, R723.1, R724.1
S_DI1_SRC: J706.4, R722.2
S_EN: C720.1, D704.3 (K), R719.2, R720.1
S_EN_BUS: J705.2, J705.3, J706.6
S_EN_IN: J706.7, R719.1
S_EN_SRC: J705.1, R718.2
S_FAN_BT: C711.1, U702.1 (BOOT)
S_FAN_COMP: R706.1, U702.6 (COMP)
S_FAN_CZ: C712.1, R706.2
S_FAN_EN: R711.2, U702.3 (EN)
S_FAN_FB: R707.2, R708.1, R709.2, U702.5 (FB)
S_FAN_PWM: R710.1
S_FAN_RT: R705.1, U702.4 (RT/CLK)
S_FAN_SW: C711.2, D703.1 (K), L702.1, U702.8 (SW)
S_FAN_V: C714.1, C715.1, C716.1, J702.1, J703.1, J704.1, L702.2, R707.1
S_FAN_VF: C713.1, R709.1, R710.2, R711.1
S_GND: C701.2, C702.2, C703.2, C704.2, C706.2, C707.2, C708.2, C709.2, C710.2, C712.2, C713.2, C714.2, C715.2, C716.2, C717.2, C718.2, C719.2, C720.2, C721.2, C722.1, D701.2 (A), D702.2 (A), D703.2 (A), D704.1 (A), D706.1 (A), D707.1 (A1), J701.2, J702.2, J703.2, J704.2, J705.4, J705.5, J706.8, Q701.2 (S), R701.2, R704.2, R705.2, R708.2, R720.2, R721.2, R723.2, R725.1, U701.7 (GND), U701.9 (PAD), U702.7 (GND), U702.9 (PAD)
S_RLY_COM: J706.2, K701.4 (COM1), K701.13 (COM2)
S_RLY_K: D705.1 (A), K701.16 (COIL2), Q701.3 (D)
S_RLY_NC: J706.3, K701.6 (NC1), K701.11 (NC2)
S_RLY_NO: J706.1, K701.8 (NO1), K701.9 (NO2)
S_STATUS_G: Q701.1 (G), R721.1
S_TACH1: J702.3, R712.2, R713.1
S_TACH1_I: C717.1, R713.2
S_TACH2: J703.3, R714.2, R715.1
S_TACH2_I: C718.1, R715.2
S_TACH3: J704.3, R716.2, R717.1
S_TACH3_I: C719.1, R717.2
S_V5_BT: C705.1, U701.1 (BOOT)
S_V5_COMP: R702.1, U701.6 (COMP)
S_V5_CZ: C706.1, R702.2
S_V5_FB: R703.2, R704.1, U701.5 (FB)
S_V5_RT: R701.1, U701.4 (RT/CLK)
S_V5_SW: C705.2, D702.1 (K), L701.1, U701.8 (SW)

Notes on the sheet:
STATUS channel -> 2N7002BK -> HFD27/005-S coil from S_5V, BAS16 across it: energised = healthy (NO closed); a trip, stop, lost SELV or live side = NC closed. Both poles in parallel; SELV circuits only (<= 30 V AC / 60 V DC). J_IO 4 = 5 V wetting (1.0k from S_5V), 5 = DI1 (10k down, 10k + 100 nF = 1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
CAN and RS-485 bus sides, SELV side of the three digital isolators; EN floating = on (internal pull-up). 22 uH, 2 x 22 uF.
STOP INPUT (HARDWARE, CHAINABLE) AND READY PERMISSIVE
S_FAN_PWM (isolated, 0/5 V) -> 4.7k / 2.2 uF -> S_FAN_VF: EN via 10k (off below 1.1-1.3 V: duty below ~25 %, static low or a dead live side = fans OFF) and current injection into FB through 15.0k: higher duty = lower voltage (24 V ... 7 V); at a low input it runs in dropout. Rtop 100k / Rbot 2.87k.
FAN 2
RELAY OUTPUT (READY / FAULT) AND DI1 (BATTERY FAULT / BMS CONTACT)
SELV 5 V (TPS54360B, 500 KHZ)
1 M || 4.7 nF 1 kV plus SMBJ58CA: a common-mode surge on the field cables is clamped to PE; a solid PELV bond by the installer is harmless. Plated M3 hole = PE / shield bond near the terminals.
AUX-T1 fan winding, cross-regulated: 12-36 V (sags to ~15 V without gate-bias load, PV-PWR). SMBJ36A clamp (36 V working), 2 x 10 uF 50 V. Both bucks have no under-voltage lock-out above 4.5 V.
FAN 3
1 +V, 2 0 V, 3 tach: 10k to S_5V, 10k + 1 nF (10 us) to the isolator input.
J_STOP 1 S_EN_SRC (S_24V via 10k: dry-contact supply for ONE module), 2 / 3 stop line in / out (loop-through: chain a cabinet 24 V stop line module to module), 4 / 5 0 V in / out, 6 screen to PE. J_IO 6-7: ready permissive in series (wire link if unused) -> S_EN_IN -> 33k / 10k, 5.1 V clamp, 100 nF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
SELV INPUT (2-PIN, DOUBLE-INSULATED LEADS, >= 10 MM FROM LIVE COPPER)
SELV 0 V TO PE (SELV MAY BE EARTHED BY THE INSTALLER: PELV)
FAN SUPPLY (TPS54360B, 300 KHZ): SPEED BY VOLTAGE, PASSES WHAT THE WINDING GIVES
FAN 1
