vectivolt/PCM/hardware/PCS-CTL/sheets/08_pcsx.kicad_sch

## KiCad design hardware/PCS-CTL/sheets/08_pcsx.kicad_sch (2026-10-07)

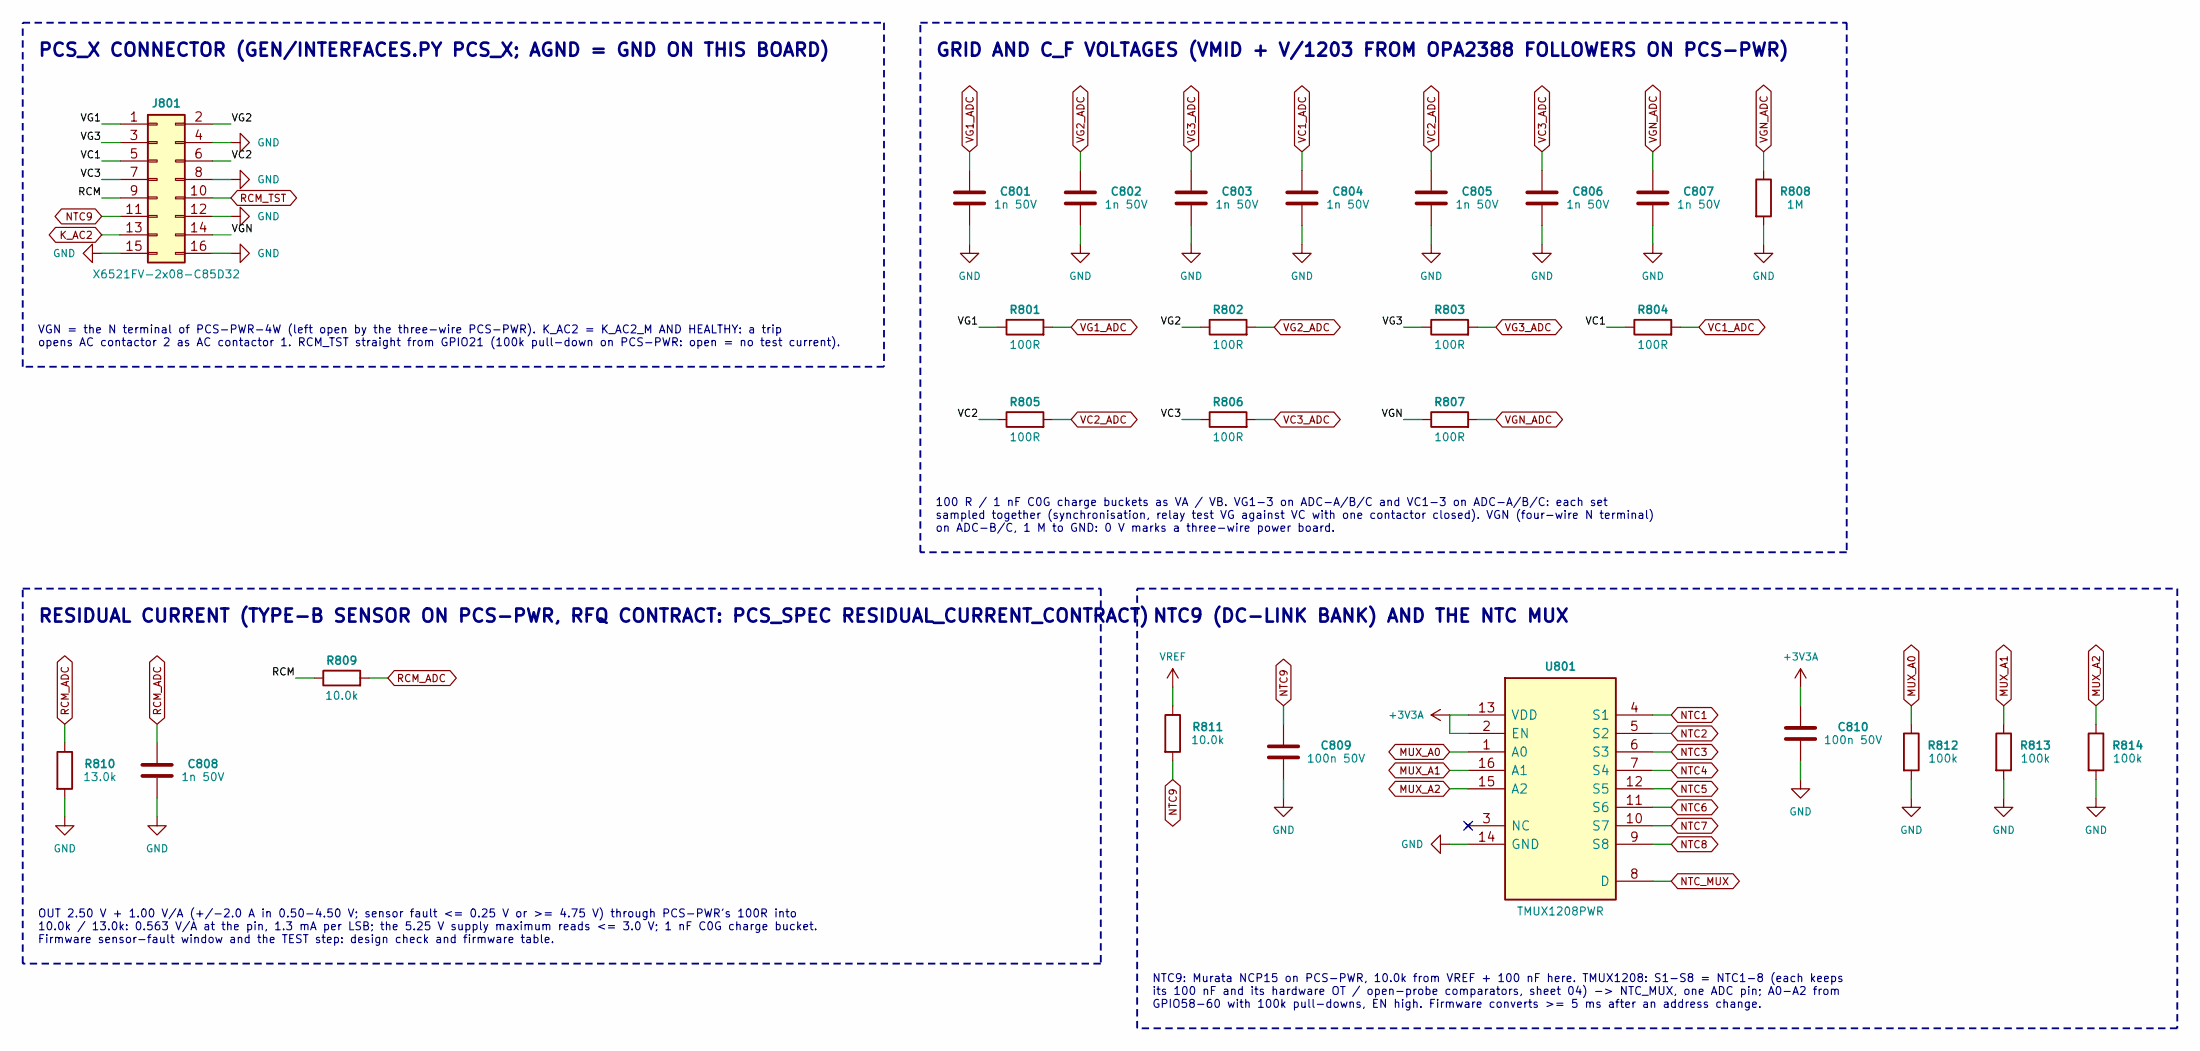
[picture p285: schematic 08_pcsx.kicad_sch]

Parts:
C801, C802, C803, C804, C805, C806, C807, C808: 1n 50V
C809, C810: 100n 50V
J801: X6521FV-2x08-C85D32; MPN X6521FV-2x08-C85D32
R801, R802, R803, R804, R805, R806, R807: 100R
R808: 1M
R809, R811: 10.0k
R810: 13.0k
R812, R813, R814: 100k
U801: TMUX1208PWR; MPN TMUX1208PWR

Connections:
+3V3A: C810.1, U801.2 (EN), U801.13 (VDD)
GND: C801.2, C802.2, C803.2, C804.2, C805.2, C806.2, C807.2, C808.2, C809.2, C810.2, J801.4, J801.8, J801.12, J801.15, J801.16, R808.2, R810.2, R812.2, R813.2, R814.2, U801.14 (GND)
K_AC2: J801.13
MUX_A0: R812.1, U801.1 (A0)
MUX_A1: R813.1, U801.16 (A1)
MUX_A2: R814.1, U801.15 (A2)
NTC1: U801.4 (S1)
NTC2: U801.5 (S2)
NTC3: U801.6 (S3)
NTC4: U801.7 (S4)
NTC5: U801.12 (S5)
NTC6: U801.11 (S6)
NTC7: U801.10 (S7)
NTC8: U801.9 (S8)
NTC9: C809.1, J801.11, R811.2
NTC_MUX: U801.8 (D)
RCM: J801.9, R809.1
RCM_ADC: C808.1, R809.2, R810.1
RCM_TST: J801.10
VC1: J801.5, R804.1
VC1_ADC: C804.1, R804.2
VC2: J801.6, R805.1
VC2_ADC: C805.1, R805.2
VC3: J801.7, R806.1
VC3_ADC: C806.1, R806.2
VG1: J801.1, R801.1
VG1_ADC: C801.1, R801.2
VG2: J801.2, R802.1
VG2_ADC: C802.1, R802.2
VG3: J801.3, R803.1
VG3_ADC: C803.1, R803.2
VGN: J801.14, R807.1
VGN_ADC: C807.1, R807.2, R808.1
VREF: R811.1

Notes on the sheet:
NTC9: Murata NCP15 on PCS-PWR, 10.0k from VREF + 100 nF here. TMUX1208: S1-S8 = NTC1-8 (each keeps its 100 nF and its hardware OT / open-probe comparators, sheet 04) -> NTC_MUX, one ADC pin; A0-A2 from GPIO58-60 with 100k pull-downs, EN high. Firmware converts >= 5 ms after an address change.
VGN = the N terminal of PCS-PWR-4W (left open by the three-wire PCS-PWR). K_AC2 = K_AC2_M AND HEALTHY: a trip opens AC contactor 2 as AC contactor 1. RCM_TST straight from GPIO21 (100k pull-down on PCS-PWR: open = no test current).
NTC9 (DC-LINK BANK) AND THE NTC MUX
OUT 2.50 V + 1.00 V/A (+/-2.0 A in 0.50-4.50 V; sensor fault <= 0.25 V or >= 4.75 V) through PCS-PWR's 100R into 10.0k / 13.0k: 0.563 V/A at the pin, 1.3 mA per LSB; the 5.25 V supply maximum reads <= 3.0 V; 1 nF C0G charge bucket. Firmware sensor-fault window and the TEST step: design check and fi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
GRID AND C_F VOLTAGES (VMID + V/1203 FROM OPA2388 FOLLOWERS ON PCS-PWR)
RESIDUAL CURRENT (TYPE-B SENSOR ON PCS-PWR, RFQ CONTRACT: PCS_SPEC RESIDUAL_CURRENT_CONTRACT)
PCS_X CONNECTOR (GEN/INTERFACES.PY PCS_X; AGND = GND ON THIS BOARD)
100 R / 1 nF C0G charge buckets as VA / VB. VG1-3 on ADC-A/B/C and VC1-3 on ADC-A/B/C: each set sampled together (synchronisation, relay test VG against VC with one contactor closed). VGN (four-wire N terminal) on ADC-B/C, 1 M to GND: 0 V marks a three-wire power board.
