vectivolt/PCM/hardware/PCS-CTL/sheets/09_eth.kicad_sch

## KiCad design hardware/PCS-CTL/sheets/09_eth.kicad_sch (2026-10-06)

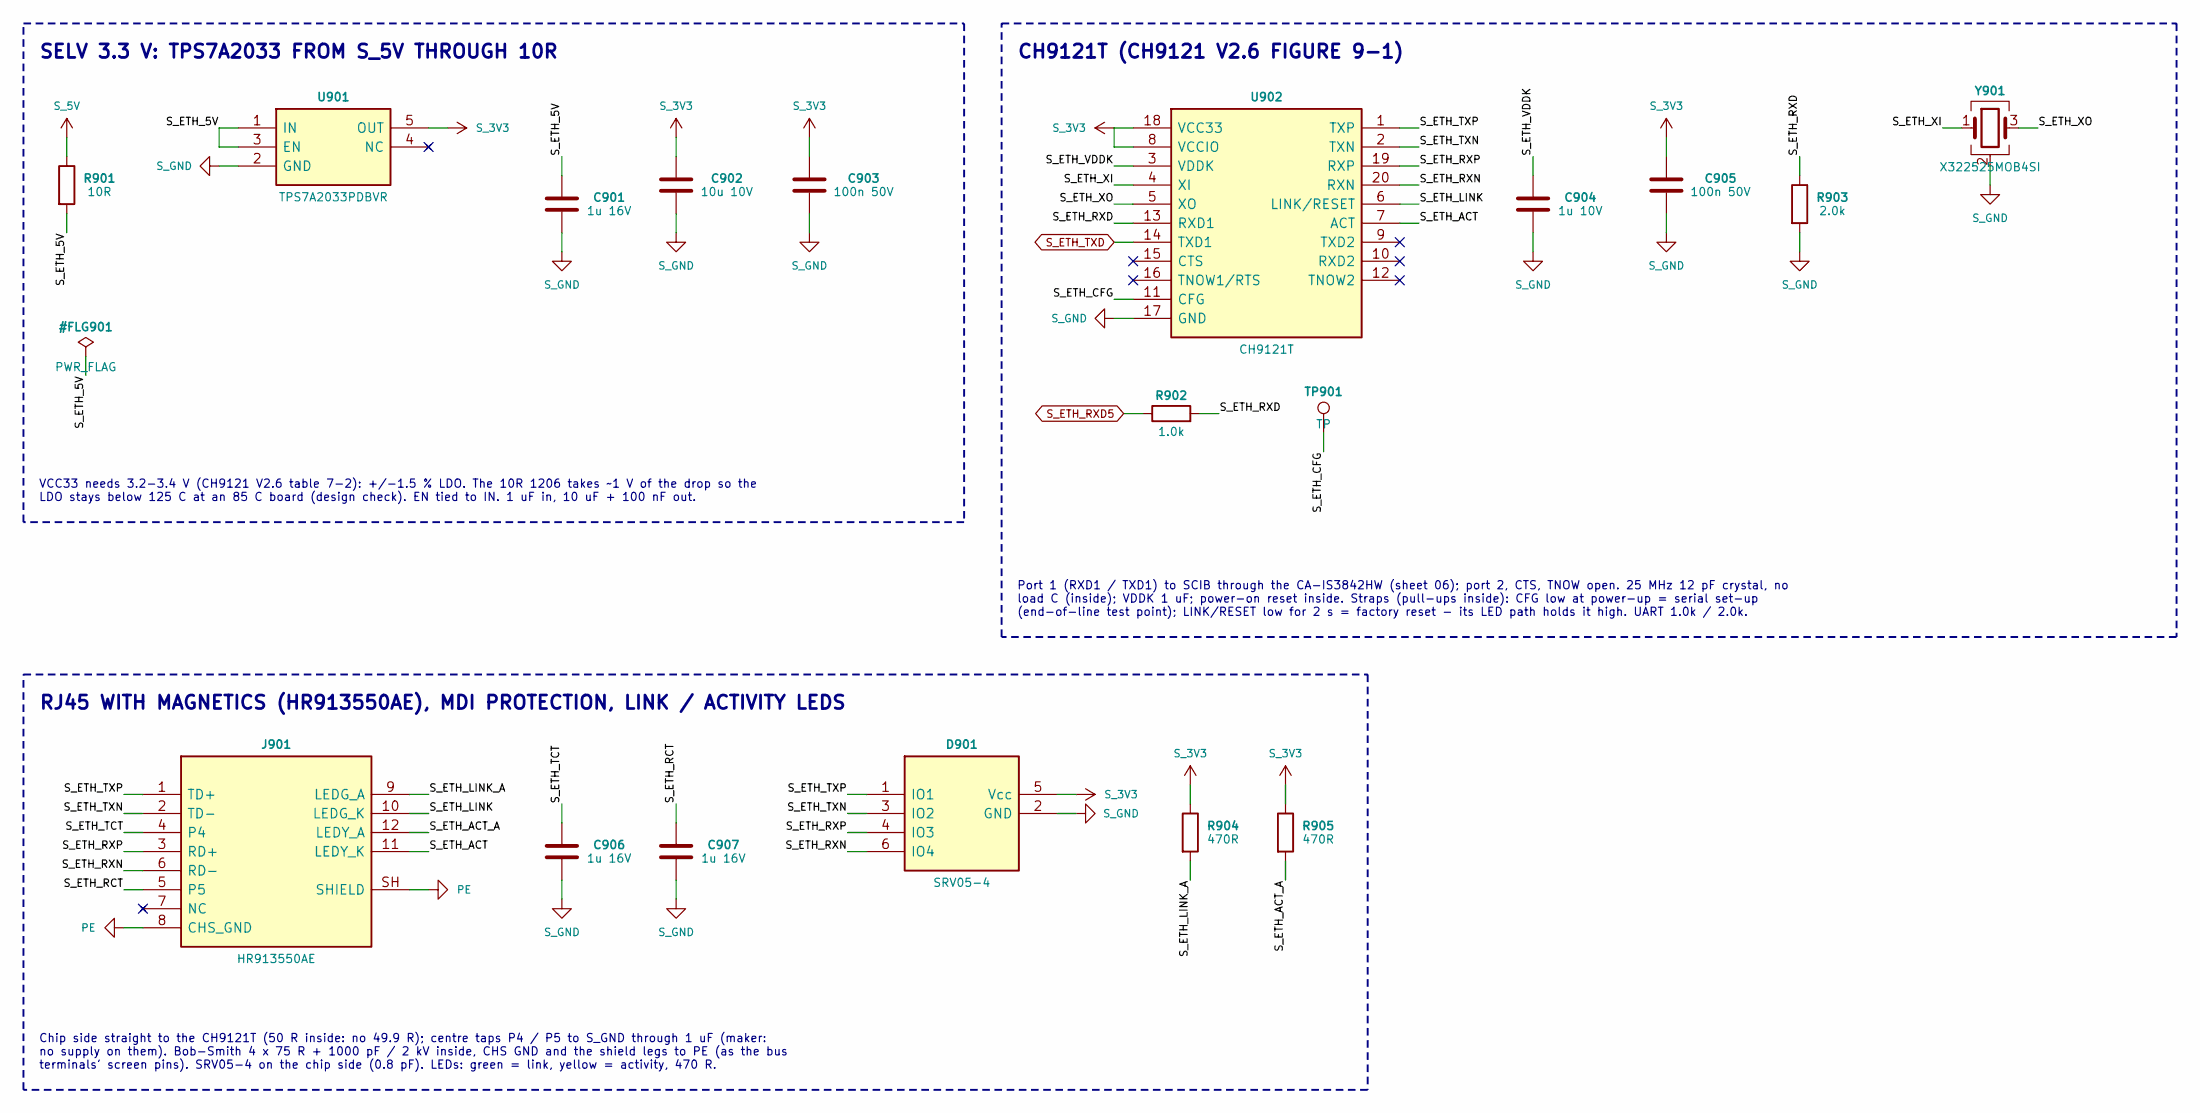
[picture p286: schematic 09_eth.kicad_sch]

Parts:
C901, C906, C907: 1u 16V
C902: 10u 10V
C903, C905: 100n 50V
C904: 1u 10V
D901: SRV05-4; MPN SRV05-4
J901: HR913550AE; MPN HR913550AE
R901: 10R
R902: 1.0k
R903: 2.0k
R904, R905: 470R
TP901: TP
U901: TPS7A2033PDBVR; MPN TPS7A2033PDBVR
U902: CH9121T; MPN CH9121T
Y901: X322525MOB4SI; MPN X322525MOB4SI

Connections:
PE: J901.8 (CHS_GND), J901.SH (SHIELD)
S_3V3: C902.1, C903.1, C905.1, D901.5 (Vcc), R904.1, R905.1, U901.5 (OUT), U902.8 (VCCIO), U902.18 (VCC33)
S_5V: R901.1
S_ETH_5V: C901.1, R901.2, U901.1 (IN), U901.3 (EN)
S_ETH_ACT: J901.11 (LEDY_K), U902.7 (ACT)
S_ETH_ACT_A: J901.12 (LEDY_A), R905.2
S_ETH_CFG: TP901.1, U902.11 (CFG)
S_ETH_LINK: J901.10 (LEDG_K), U902.6 (LINK/RESET)
S_ETH_LINK_A: J901.9 (LEDG_A), R904.2
S_ETH_RCT: C907.1, J901.5
S_ETH_RXD: R902.2, R903.1, U902.13 (RXD1)
S_ETH_RXD5: R902.1
S_ETH_RXN: D901.6 (IO4), J901.6 (RD-), U902.20 (RXN)
S_ETH_RXP: D901.4 (IO3), J901.3 (RD+), U902.19 (RXP)
S_ETH_TCT: C906.1, J901.4
S_ETH_TXD: U902.14 (TXD1)
S_ETH_TXN: D901.3 (IO2), J901.2 (TD-), U902.2 (TXN)
S_ETH_TXP: D901.1 (IO1), J901.1 (TD+), U902.1 (TXP)
S_ETH_VDDK: C904.1, U902.3 (VDDK)
S_ETH_XI: U902.4 (XI), Y901.1
S_ETH_XO: U902.5 (XO), Y901.3
S_GND: C901.2, C902.2, C903.2, C904.2, C905.2, C906.2, C907.2, D901.2 (GND), R903.2, U901.2 (GND), U902.17 (GND), Y901.2 (G), Y901.4 (G)

Notes on the sheet:
Chip side straight to the CH9121T (50 R inside: no 49.9 R); centre taps P4 / P5 to S_GND through 1 uF (maker: no supply on them). Bob-Smith 4 x 75 R + 1000 pF / 2 kV inside, CHS GND and the shield legs to PE (as the bus terminals' screen pins). SRV05-4 on the chip side (0.8 pF). LEDs: green = link,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
Port 1 (RXD1 / TXD1) to SCIB through the CA-IS3842HW (sheet 06); port 2, CTS, TNOW open. 25 MHz 12 pF crystal, no load C (inside); VDDK 1 uF; power-on reset inside. Straps (pull-ups inside): CFG low at power-up = serial set-up (end-of-line test point); LINK/RESET low for 2 s = factory reset - its L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
RJ45 WITH MAGNETICS (HR913550AE), MDI PROTECTION, LINK / ACTIVITY LEDS
SELV 3.3 V: TPS7A2033 FROM S_5V THROUGH 10R
VCC33 needs 3.2-3.4 V (CH9121 V2.6 table 7-2): +/-1.5 % LDO. The 10R 1206 takes ~1 V of the drop so the LDO stays below 125 C at an 85 C board (design check). EN tied to IN. 1 uF in, 10 uF + 100 nF out.
CH9121T (CH9121 V2.6 FIGURE 9-1)
