vectivolt/PCM/hardware/PCS-PWR-4W/sheets/01_pc.kicad_sch

## KiCad design hardware/PCS-PWR-4W/sheets/01_pc.kicad_sch (2026-10-06)

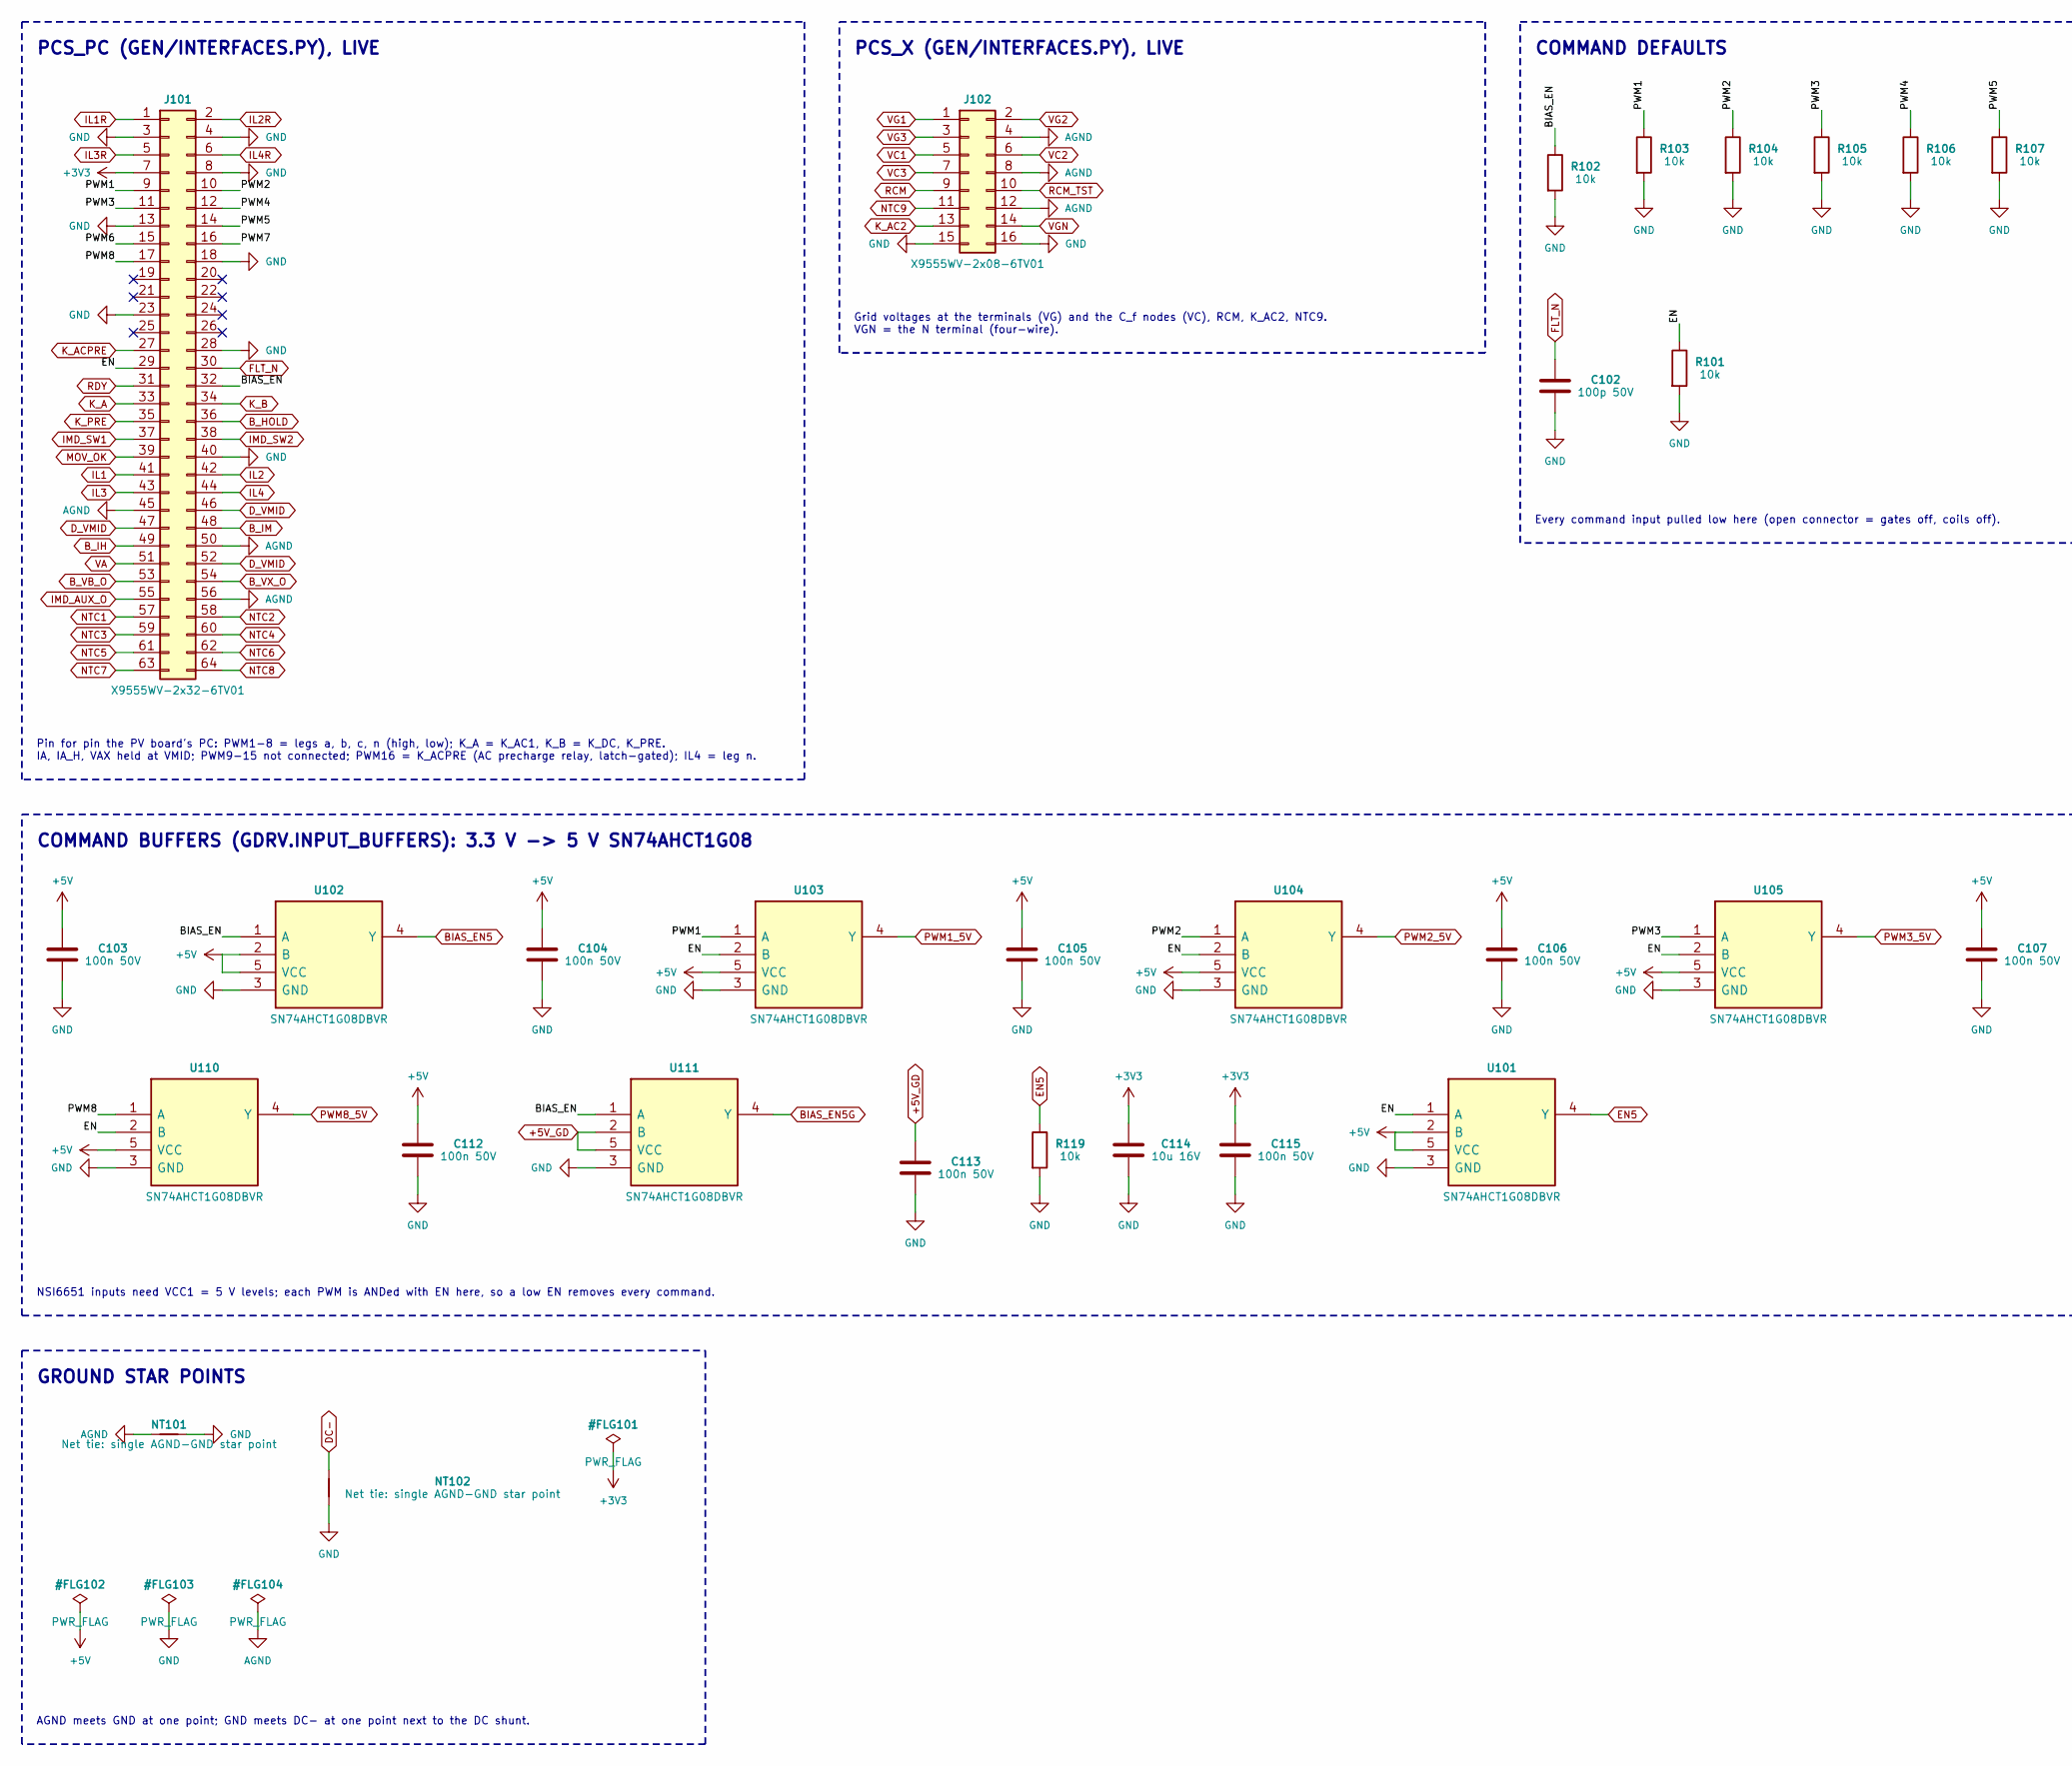
[picture p287: schematic 01_pc.kicad_sch, part in row 1, column 1]

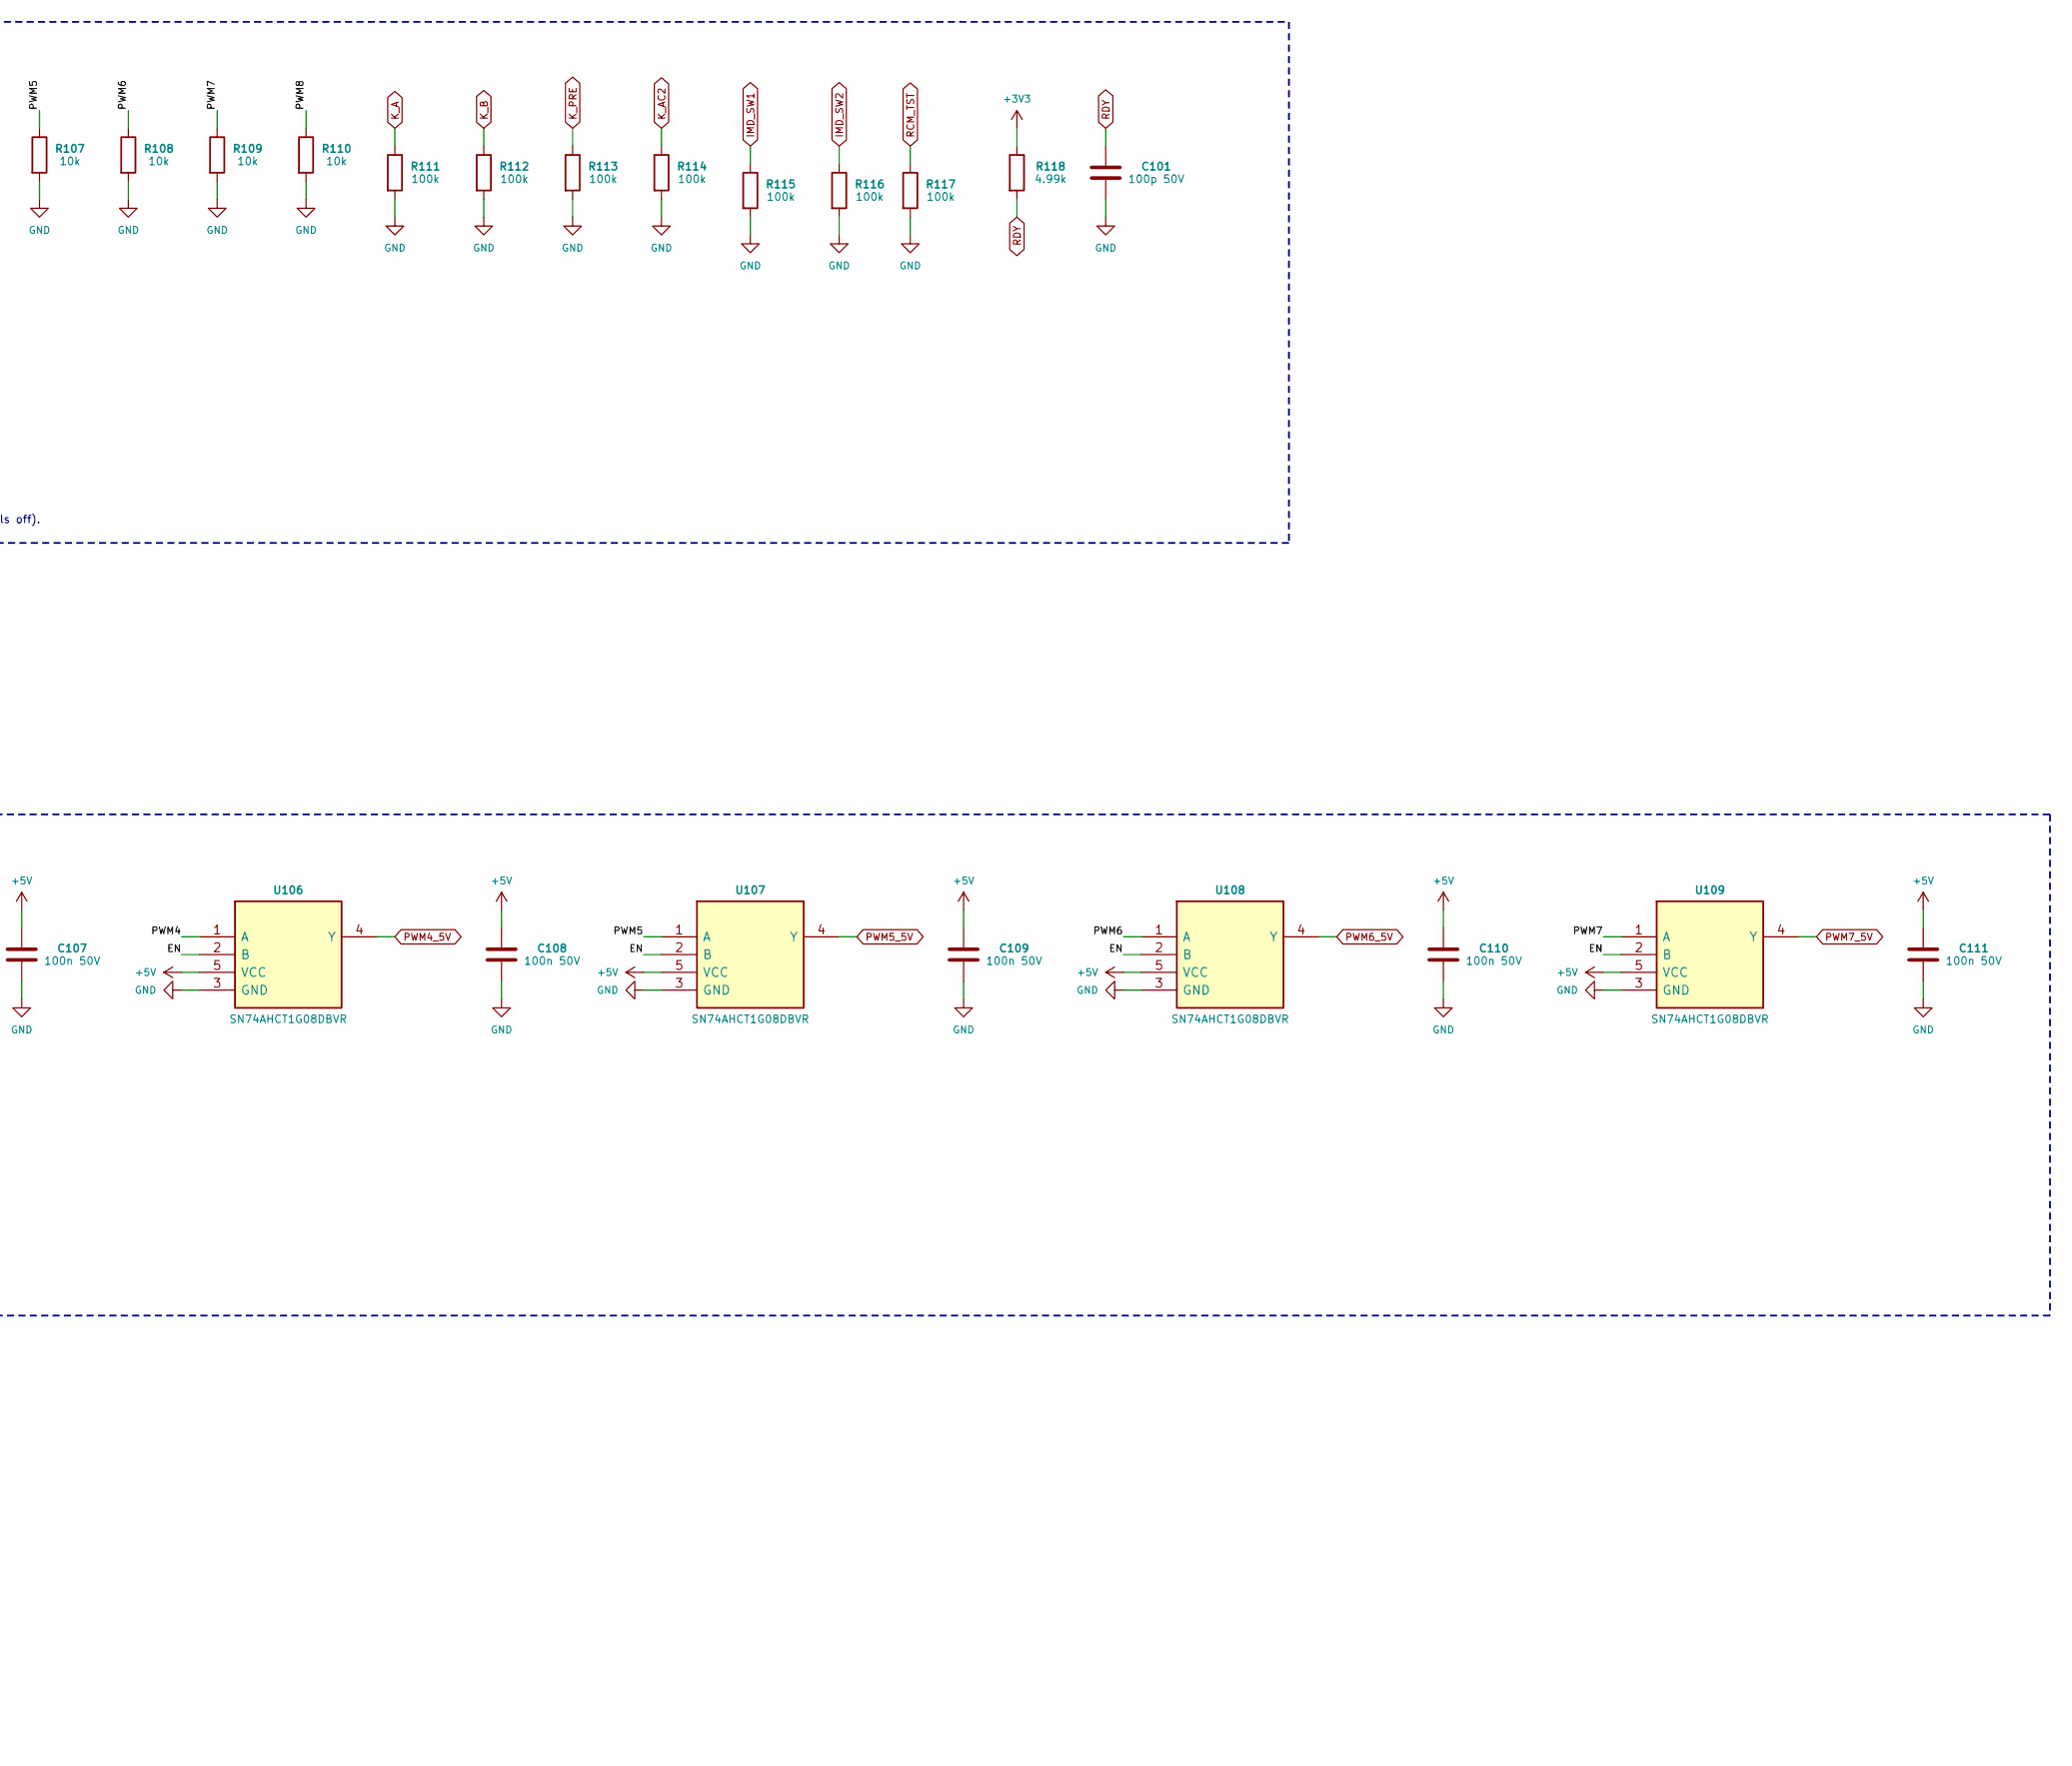
[picture p288: schematic 01_pc.kicad_sch, part in row 1, column 2]

Parts:
C101, C102: 100p 50V
C103, C104, C105, C106, C107, C108, C109, C110, C111, C112, C113, C115: 100n 50V
C114: 10u 16V
J101: X9555WV-2x32-6TV01; MPN X9555WV-2x32-6TV01
J102: X9555WV-2x08-6TV01; MPN X9555WV-2x08-6TV01
NT101, NT102: Net tie: single AGND-GND star point
R101, R102, R103, R104, R105, R106, R107, R108, R109, R110, R119: 10k
R111, R112, R113, R114, R115, R116, R117: 100k
R118: 4.99k
U101, U102, U103, U104, U105, U106, U107, U108, U109, U110, U111: SN74AHCT1G08DBVR; MPN SN74AHCT1G08DBVR

Connections:
+3V3: C114.1, C115.1, J101.7, R118.1
+5V: C103.1, C104.1, C105.1, C106.1, C107.1, C108.1, C109.1, C110.1, C111.1, C112.1, U101.2 (B), U101.5 (VCC), U102.2 (B), U102.5 (VCC), U103.5 (VCC), U104.5 (VCC), U105.5 (VCC), U106.5 (VCC), U107.5 (VCC), U108.5 (VCC), U109.5 (VCC), U110.5 (VCC)
+5V_GD: C113.1, U111.2 (B), U111.5 (VCC)
AGND: J101.45, J101.50, J101.56, J102.4, J102.8, J102.12, NT101.1
BIAS_EN: J101.32, R102.1, U102.1 (A), U111.1 (A)
BIAS_EN5: U102.4 (Y)
BIAS_EN5G: U111.4 (Y)
B_HOLD: J101.36
B_IH: J101.49
B_IM: J101.48
B_VB_O: J101.53
B_VX_O: J101.54
DC-: NT102.2
D_VMID: J101.46, J101.47, J101.52
EN: J101.29, R101.1, U101.1 (A), U103.2 (B), U104.2 (B), U105.2 (B), U106.2 (B), U107.2 (B), U108.2 (B), U109.2 (B), U110.2 (B)
EN5: R119.1, U101.4 (Y)
FLT_N: C102.1, J101.30
GND: C101.2, C102.2, C103.2, C104.2, C105.2, C106.2, C107.2, C108.2, C109.2, C110.2, C111.2, C112.2, C113.2, C114.2, C115.2, J101.3, J101.4, J101.8, J101.13, J101.18, J101.23, J101.28, J101.40, J102.15, J102.16, NT101.2, NT102.1, R101.2, R102.2, R103.2, R104.2, R105.2, R106.2, R107.2, R108.2, R109.2, R110.2, R111.2, R112.2, R113.2, R114.2, R115.2, R116.2, R117.2, R119.2, U101.3 (GND), U102.3 (GND), U103.3 (GND), U104.3 (GND), U105.3 (GND), U106.3 (GND), U107.3 (GND), U108.3 (GND), U109.3 (GND), U110.3 (GND), U111.3 (GND)
IL1: J101.41
IL1R: J101.1
IL2: J101.42
IL2R: J101.2
IL3: J101.43
IL3R: J101.5
IL4: J101.44
IL4R: J101.6
IMD_AUX_O: J101.55
IMD_SW1: J101.37, R115.1
IMD_SW2: J101.38, R116.1
K_A: J101.33, R111.1
K_AC2: J102.13, R114.1
K_ACPRE: J101.27
K_B: J101.34, R112.1
K_PRE: J101.35, R113.1
MOV_OK: J101.39
NTC1: J101.57
NTC2: J101.58
NTC3: J101.59
NTC4: J101.60
NTC5: J101.61
NTC6: J101.62
NTC7: J101.63
NTC8: J101.64
NTC9: J102.11
PWM1: J101.9, R103.1, U103.1 (A)
PWM1_5V: U103.4 (Y)
PWM2: J101.10, R104.1, U104.1 (A)
PWM2_5V: U104.4 (Y)
PWM3: J101.11, R105.1, U105.1 (A)
PWM3_5V: U105.4 (Y)
PWM4: J101.12, R106.1, U106.1 (A)
PWM4_5V: U106.4 (Y)
PWM5: J101.14, R107.1, U107.1 (A)
PWM5_5V: U107.4 (Y)
PWM6: J101.15, R108.1, U108.1 (A)
PWM6_5V: U108.4 (Y)
PWM7: J101.16, R109.1, U109.1 (A)
PWM7_5V: U109.4 (Y)
PWM8: J101.17, R110.1, U110.1 (A)
PWM8_5V: U110.4 (Y)
RCM: J102.9
RCM_TST: J102.10, R117.1
RDY: C101.1, J101.31, R118.2
VA: J101.51
VC1: J102.5
VC2: J102.6
VC3: J102.7
VG1: J102.1
VG2: J102.2
VG3: J102.3
VGN: J102.14

Notes on the sheet:
NSI6651 inputs need VCC1 = 5 V levels; each PWM is ANDed with EN here, so a low EN removes every command.
Grid voltages at the terminals (VG) and the C_f nodes (VC), RCM, K_AC2, NTC9. VGN = the N terminal (four-wire).
Every command input pulled low here (open connector = gates off, coils off).
PCS_PC (GEN/INTERFACES.PY), LIVE
GROUND STAR POINTS
AGND meets GND at one point; GND meets DC- at one point next to the DC shunt.
COMMAND DEFAULTS
Pin for pin the PV board's PC: PWM1-8 = legs a, b, c, n (high, low); K_A = K_AC1, K_B = K_DC, K_PRE. IA, IA_H, VAX held at VMID; PWM9-15 not connected; PWM16 = K_ACPRE (AC precharge relay, latch-gated); IL4 = leg n.
PCS_X (GEN/INTERFACES.PY), LIVE
COMMAND BUFFERS (GDRV.INPUT_BUFFERS): 3.3 V -> 5 V SN74AHCT1G08
