vectivolt/PCM/hardware/PCS-PWR-4W/sheets/03_lega.kicad_sch

## KiCad design hardware/PCS-PWR-4W/sheets/03_lega.kicad_sch (2026-10-07)

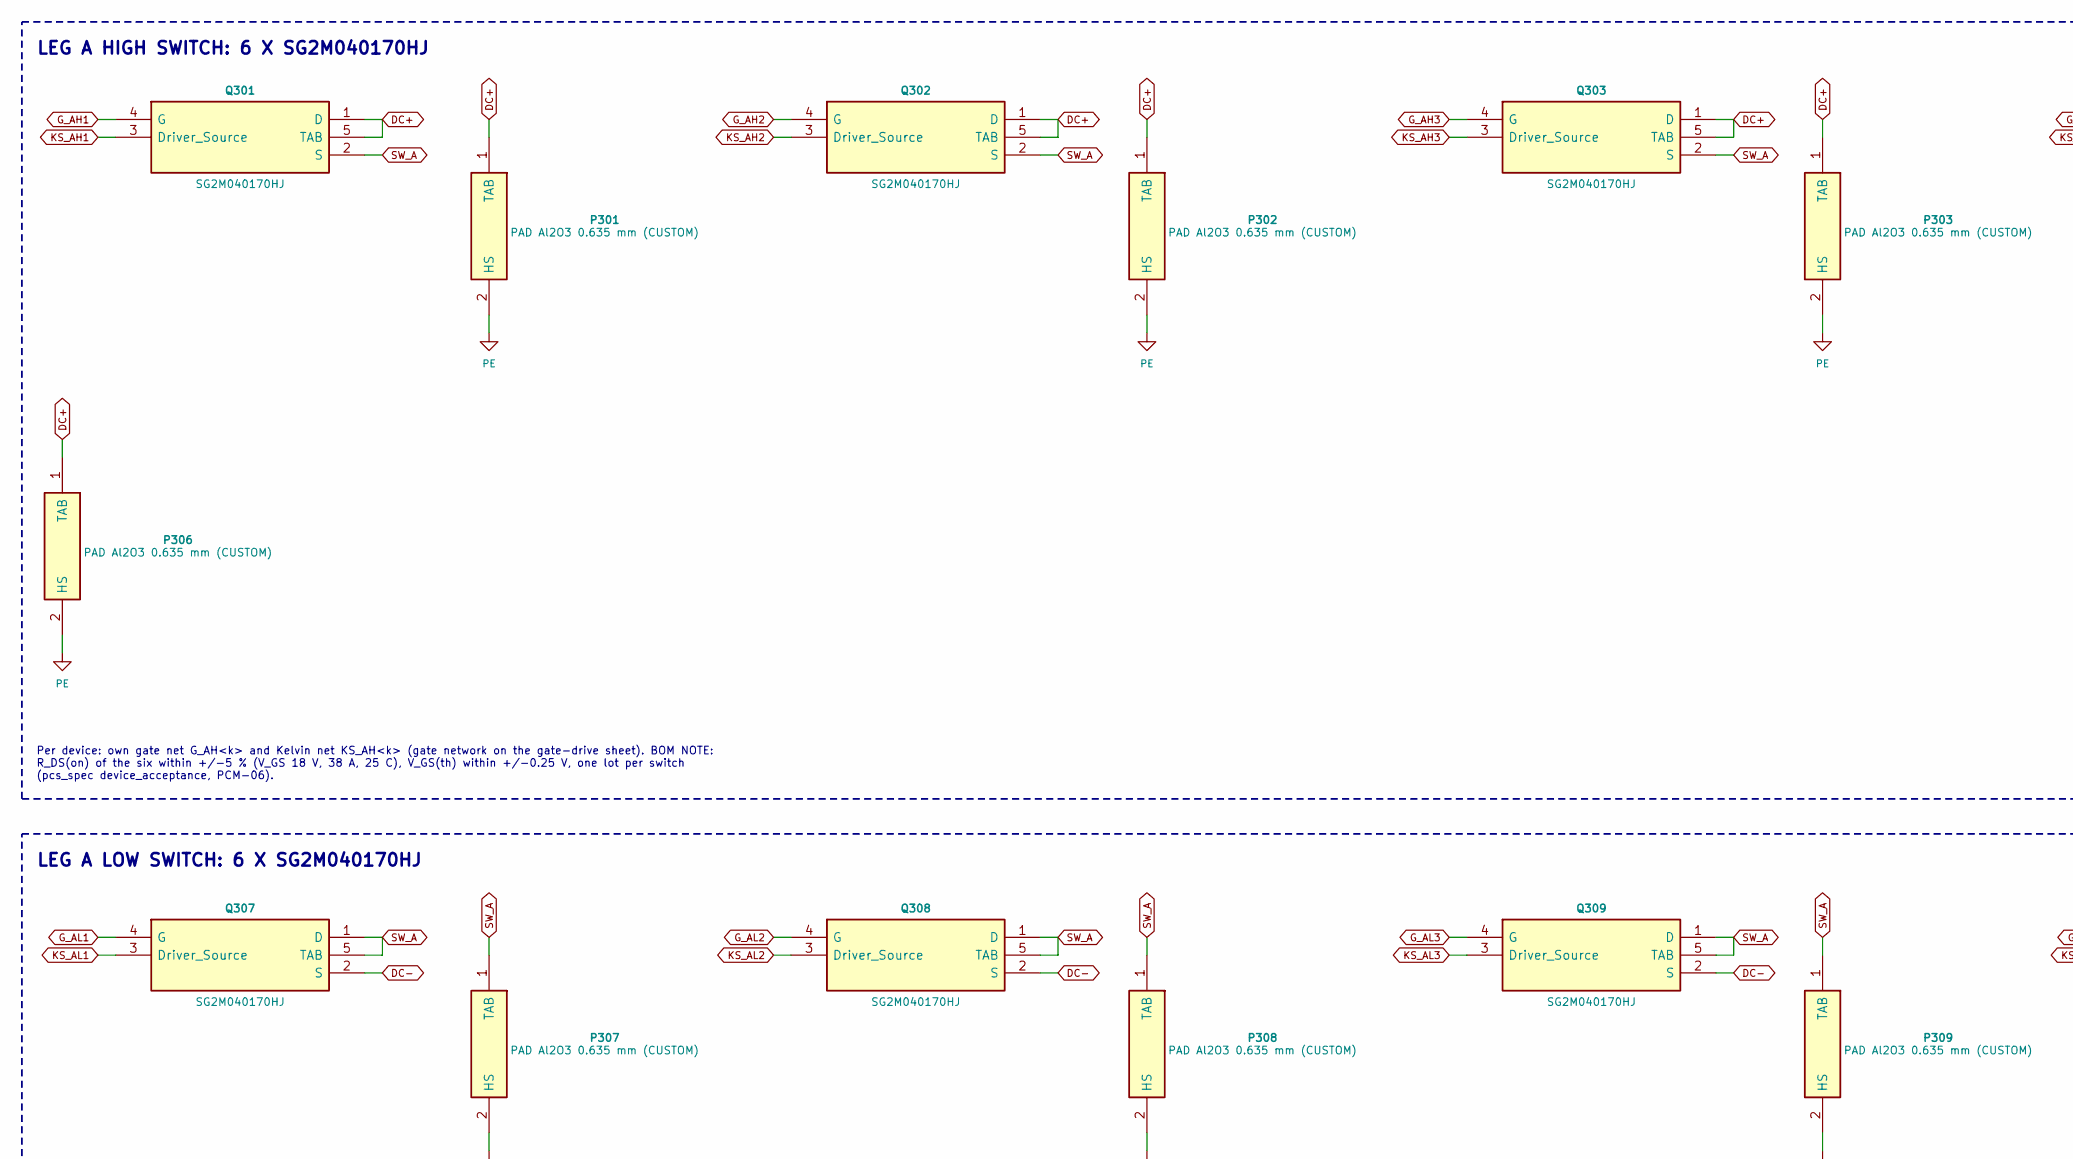
[picture p291: schematic 03_lega.kicad_sch, part in row 1, column 1]

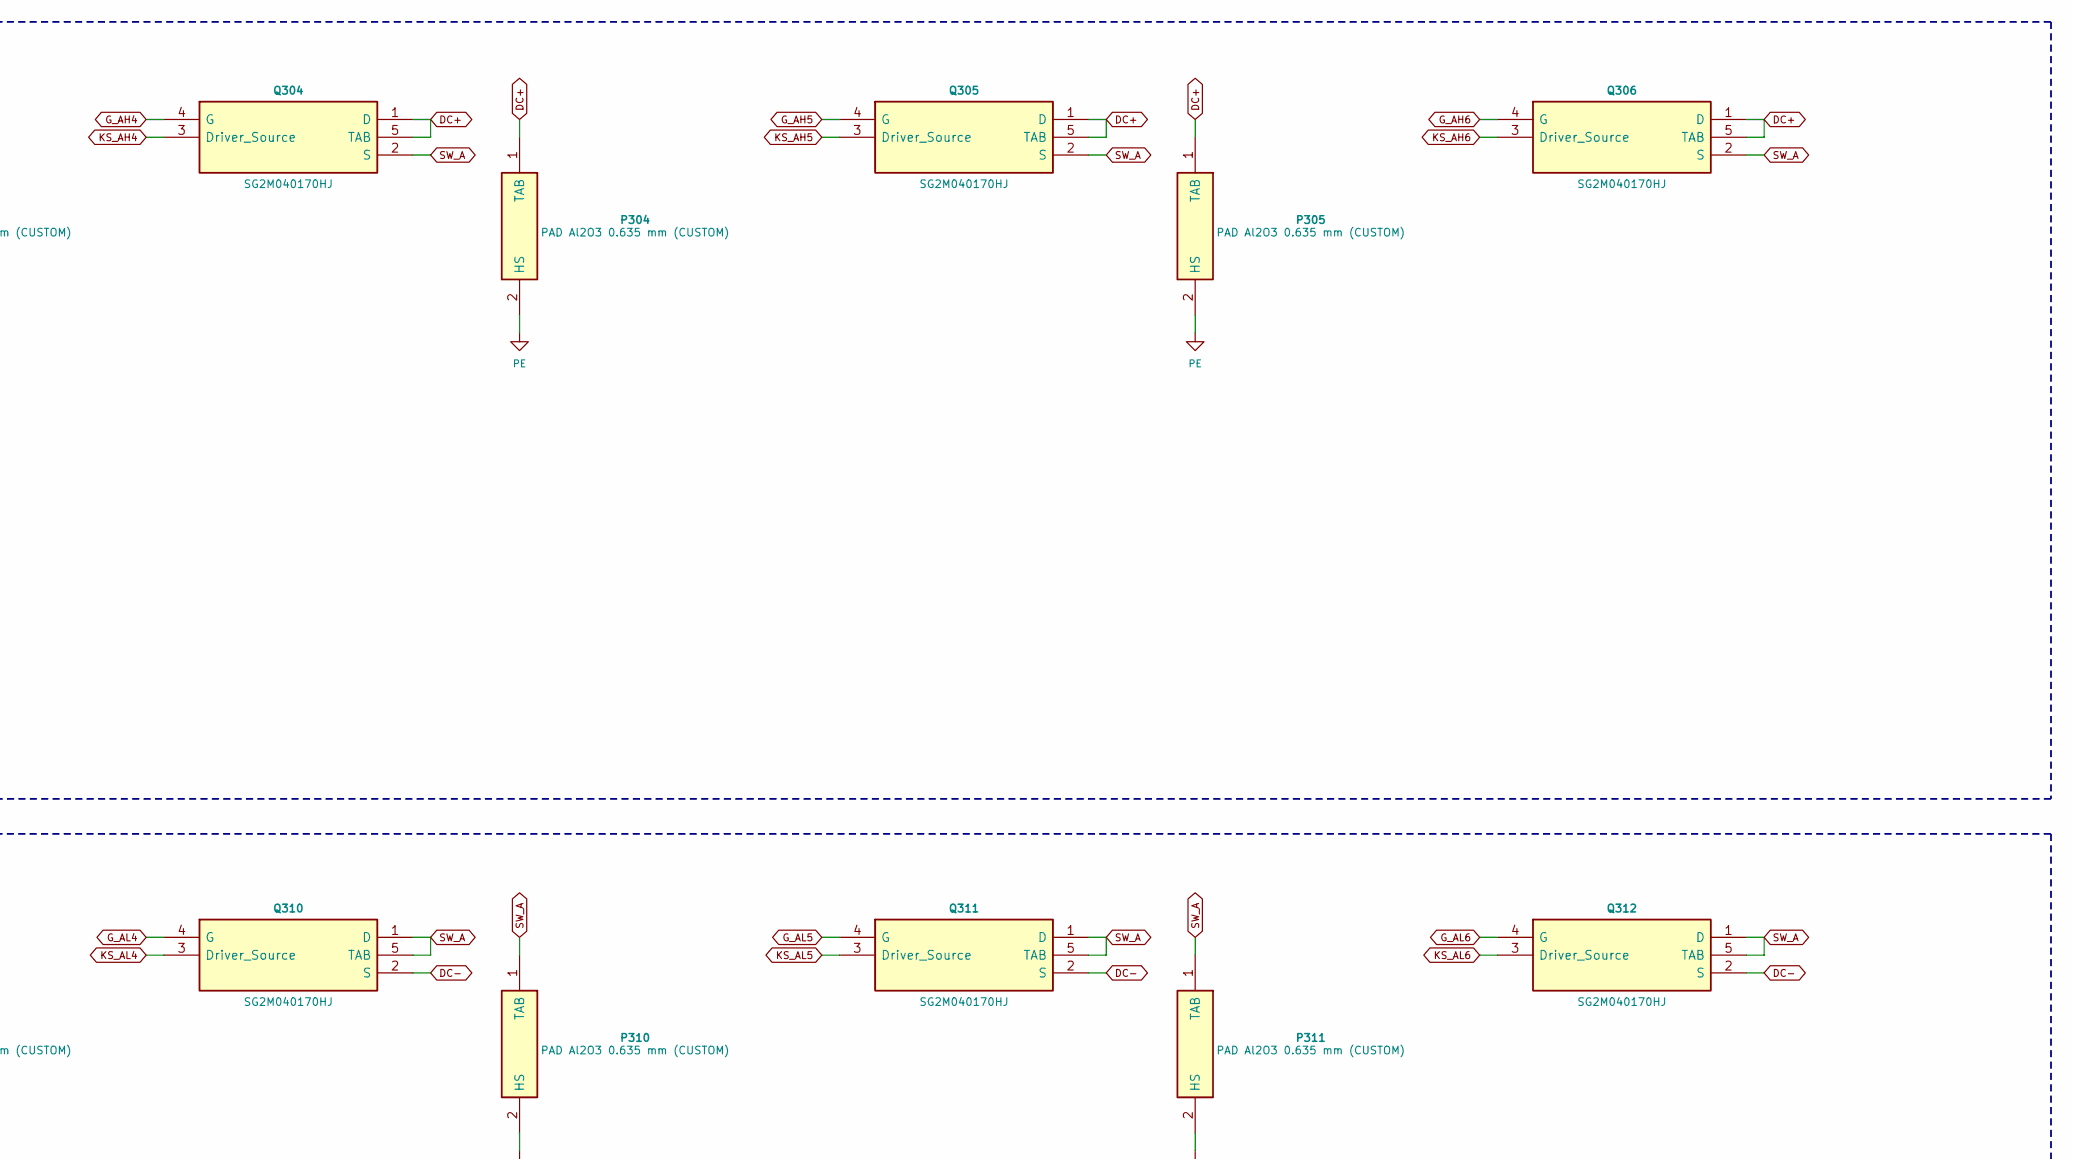
[picture p292: schematic 03_lega.kicad_sch, part in row 1, column 2]

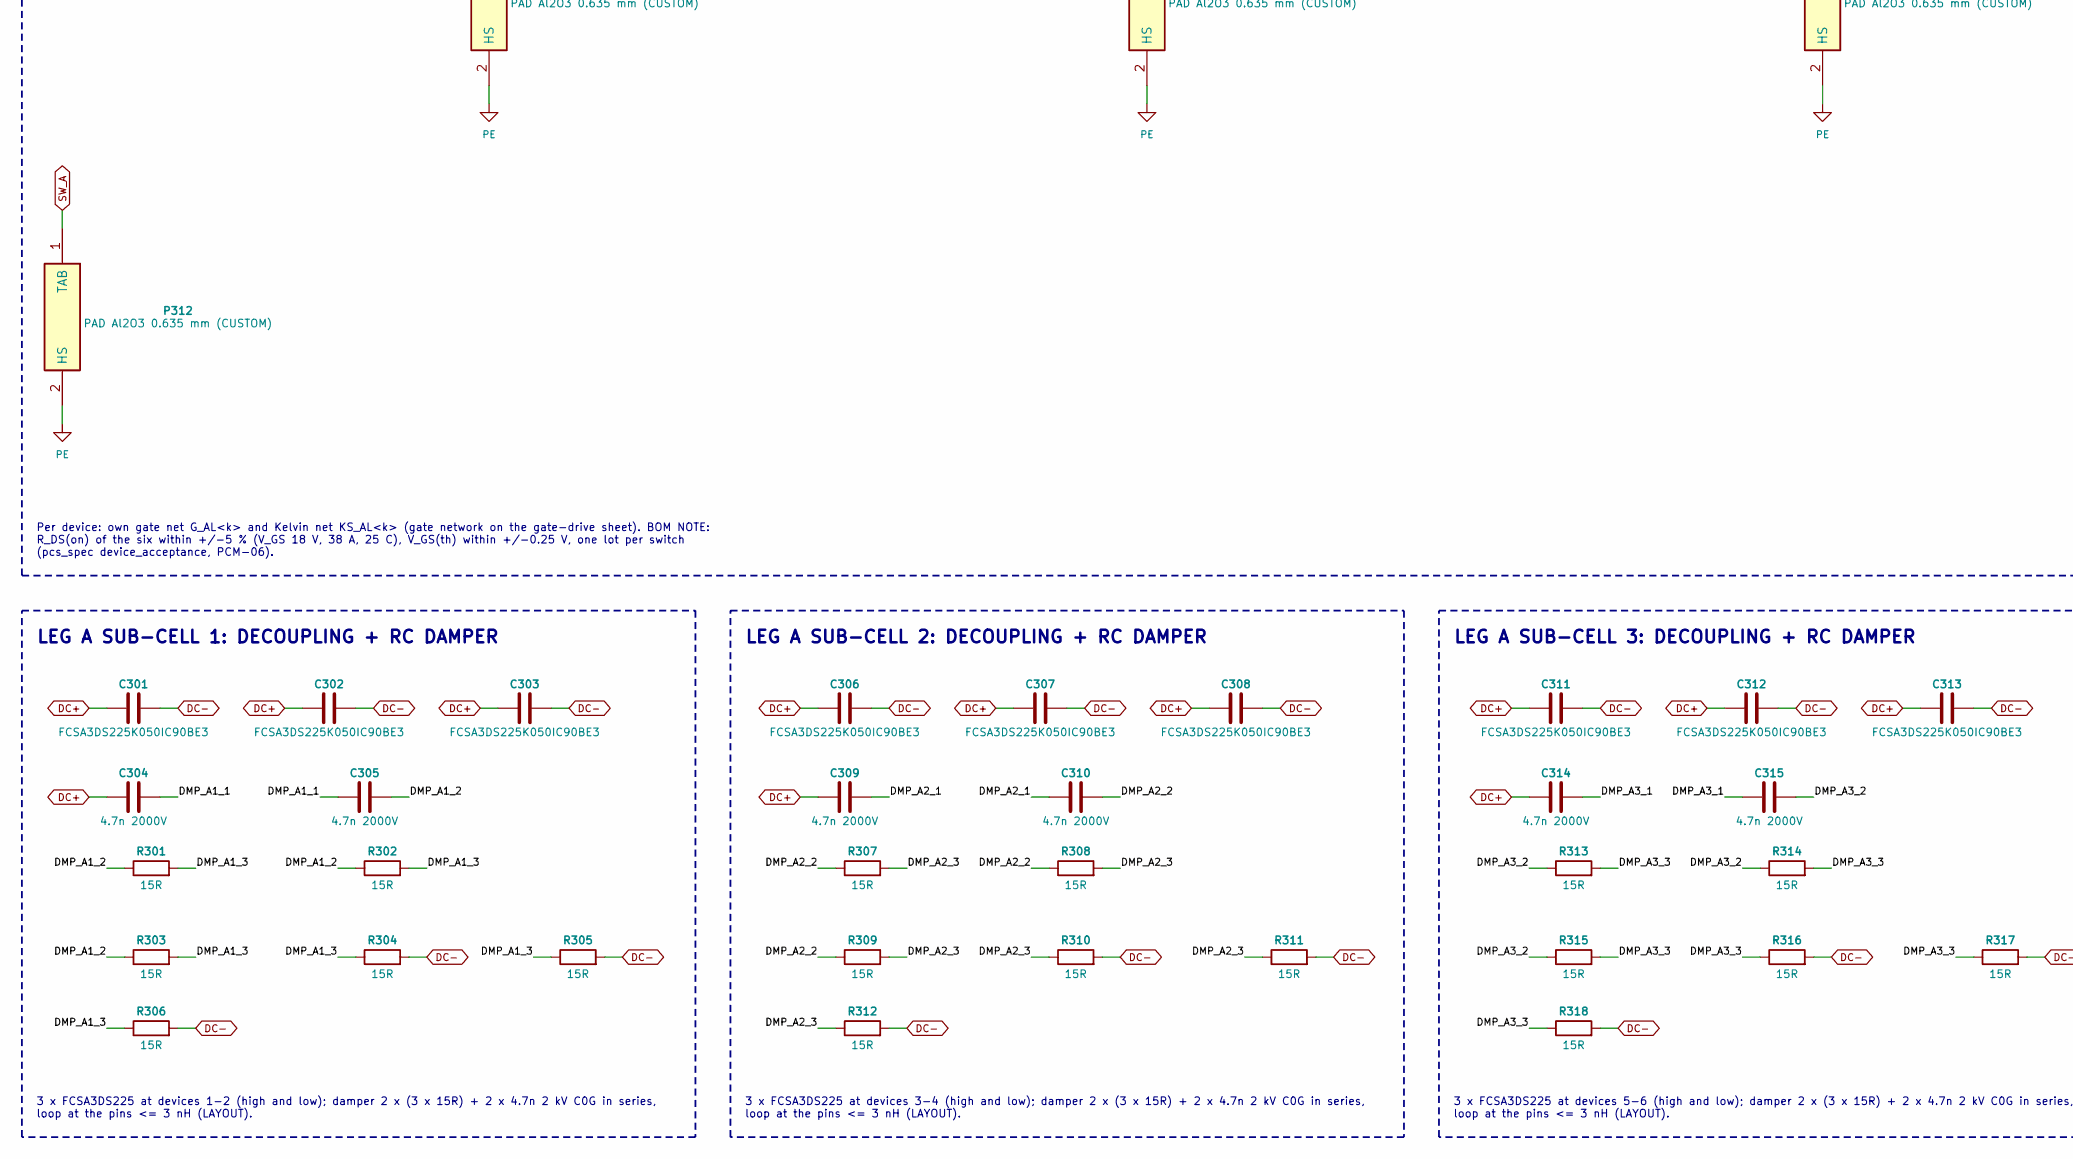
[picture p293: schematic 03_lega.kicad_sch, part in row 2, column 1]

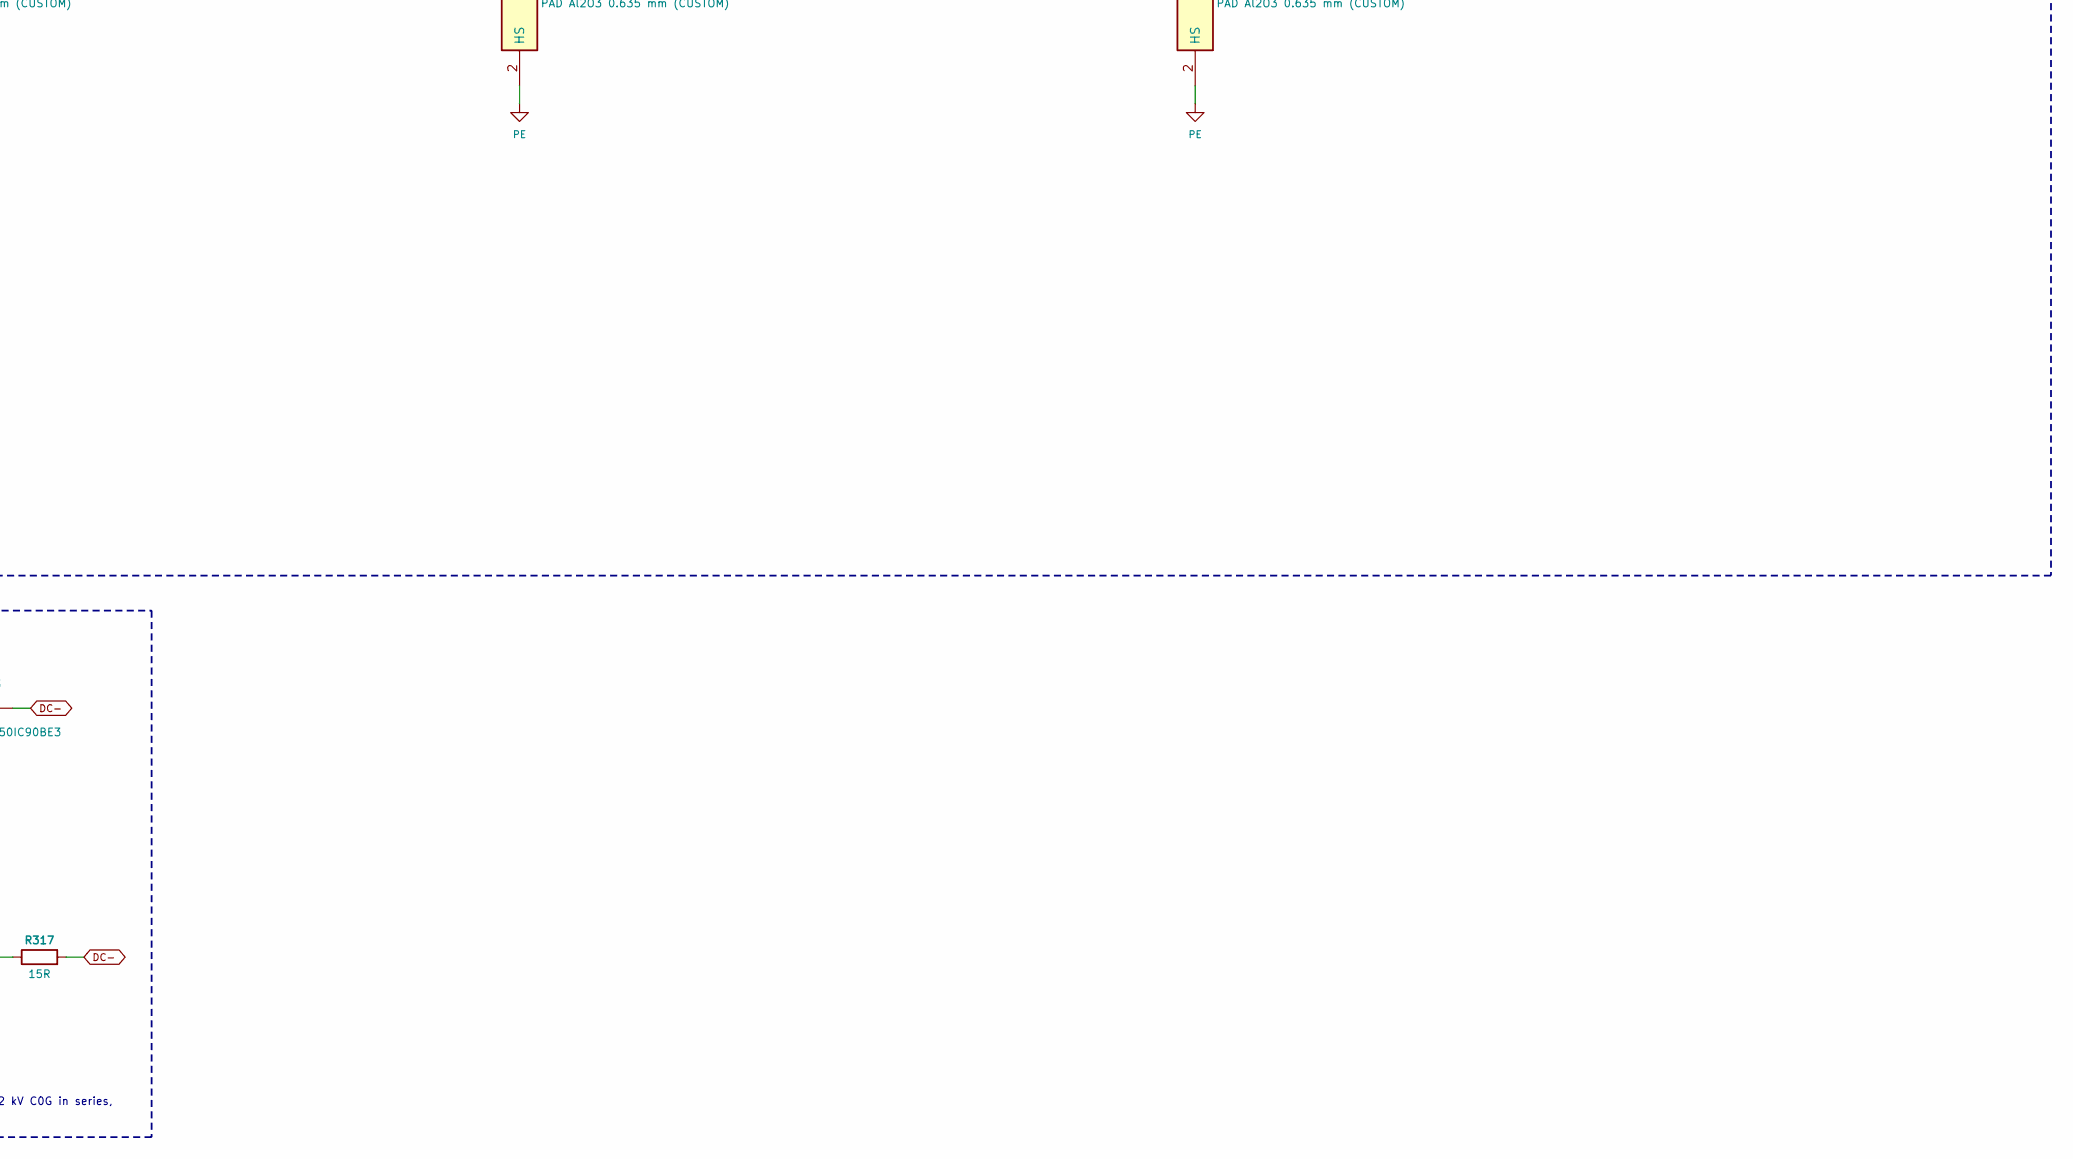
[picture p294: schematic 03_lega.kicad_sch, part in row 2, column 2]

Parts:
C301, C302, C303, C306, C307, C308, C311, C312, C313: FCSA3DS225K050IC90BE3; MPN FCSA3DS225K050IC90BE3
C304, C305, C309, C310, C314, C315: 4.7n 2000V
P301, P302, P303, P304, P305, P306, P307, P308, P309, P310, P311, P312: PAD Al2O3 0.635 mm (CUSTOM)
Q301, Q302, Q303, Q304, Q305, Q306, Q307, Q308, Q309, Q310, Q311, Q312: SG2M040170HJ; MPN SG2M040170HJ
R301, R302, R303, R304, R305, R306, R307, R308, R309, R310, R311, R312, R313, R314, R315, R316, R317, R318: 15R; MPN CRCW251215R0FKEGHP

Connections:
DC+: C301.1, C302.1, C303.1, C304.1, C306.1, C307.1, C308.1, C309.1, C311.1, C312.1, C313.1, C314.1, P301.1 (TAB), P302.1 (TAB), P303.1 (TAB), P304.1 (TAB), P305.1 (TAB), P306.1 (TAB), Q301.1 (D), Q301.5 (TAB), Q302.1 (D), Q302.5 (TAB), Q303.1 (D), Q303.5 (TAB), Q304.1 (D), Q304.5 (TAB), Q305.1 (D), Q305.5 (TAB), Q306.1 (D), Q306.5 (TAB)
DC-: C301.2, C302.2, C303.2, C306.2, C307.2, C308.2, C311.2, C312.2, C313.2, Q307.2 (S), Q308.2 (S), Q309.2 (S), Q310.2 (S), Q311.2 (S), Q312.2 (S), R304.2, R305.2, R306.2, R310.2, R311.2, R312.2, R316.2, R317.2, R318.2
DMP_A1_1: C304.2, C305.1
DMP_A1_2: C305.2, R301.1, R302.1, R303.1
DMP_A1_3: R301.2, R302.2, R303.2, R304.1, R305.1, R306.1
DMP_A2_1: C309.2, C310.1
DMP_A2_2: C310.2, R307.1, R308.1, R309.1
DMP_A2_3: R307.2, R308.2, R309.2, R310.1, R311.1, R312.1
DMP_A3_1: C314.2, C315.1
DMP_A3_2: C315.2, R313.1, R314.1, R315.1
DMP_A3_3: R313.2, R314.2, R315.2, R316.1, R317.1, R318.1
G_AH1: Q301.4 (G)
G_AH2: Q302.4 (G)
G_AH3: Q303.4 (G)
G_AH4: Q304.4 (G)
G_AH5: Q305.4 (G)
G_AH6: Q306.4 (G)
G_AL1: Q307.4 (G)
G_AL2: Q308.4 (G)
G_AL3: Q309.4 (G)
G_AL4: Q310.4 (G)
G_AL5: Q311.4 (G)
G_AL6: Q312.4 (G)
KS_AH1: Q301.3 (Driver_Source)
KS_AH2: Q302.3 (Driver_Source)
KS_AH3: Q303.3 (Driver_Source)
KS_AH4: Q304.3 (Driver_Source)
KS_AH5: Q305.3 (Driver_Source)
KS_AH6: Q306.3 (Driver_Source)
KS_AL1: Q307.3 (Driver_Source)
KS_AL2: Q308.3 (Driver_Source)
KS_AL3: Q309.3 (Driver_Source)
KS_AL4: Q310.3 (Driver_Source)
KS_AL5: Q311.3 (Driver_Source)
KS_AL6: Q312.3 (Driver_Source)
PE: P301.2 (HS), P302.2 (HS), P303.2 (HS), P304.2 (HS), P305.2 (HS), P306.2 (HS), P307.2 (HS), P308.2 (HS), P309.2 (HS), P310.2 (HS), P311.2 (HS), P312.2 (HS)
SW_A: P307.1 (TAB), P308.1 (TAB), P309.1 (TAB), P310.1 (TAB), P311.1 (TAB), P312.1 (TAB), Q301.2 (S), Q302.2 (S), Q303.2 (S), Q304.2 (S), Q305.2 (S), Q306.2 (S), Q307.1 (D), Q307.5 (TAB), Q308.1 (D), Q308.5 (TAB), Q309.1 (D), Q309.5 (TAB), Q310.1 (D), Q310.5 (TAB), Q311.1 (D), Q311.5 (TAB), Q312.1 (D), Q312.5 (TAB)

Notes on the sheet:
LEG A SUB-CELL 2: DECOUPLING + RC DAMPER
LEG A HIGH SWITCH: 6 X SG2M040170HJ
LEG A SUB-CELL 1: DECOUPLING + RC DAMPER
3 x FCSA3DS225 at devices 1-2 (high and low); damper 2 x (3 x 15R) + 2 x 4.7n 2 kV C0G in series, loop at the pins <= 3 nH (LAYOUT).
Per device: own gate net G_AH<k> and Kelvin net KS_AH<k> (gate network on the gate-drive sheet). BOM NOTE: R_DS(on) of the six within +/-5 % (V_GS 18 V, 38 A, 25 C), V_GS(th) within +/-0.25 V, one lot per switch (pcs_spec device_acceptance, PCM-06).
3 x FCSA3DS225 at devices 3-4 (high and low); damper 2 x (3 x 15R) + 2 x 4.7n 2 kV C0G in series, loop at the pins <= 3 nH (LAYOUT).
LEG A LOW SWITCH: 6 X SG2M040170HJ
LEG A SUB-CELL 3: DECOUPLING + RC DAMPER
Per device: own gate net G_AL<k> and Kelvin net KS_AL<k> (gate network on the gate-drive sheet). BOM NOTE: R_DS(on) of the six within +/-5 % (V_GS 18 V, 38 A, 25 C), V_GS(th) within +/-0.25 V, one lot per switch (pcs_spec device_acceptance, PCM-06).
3 x FCSA3DS225 at devices 5-6 (high and low); damper 2 x (3 x 15R) + 2 x 4.7n 2 kV C0G in series, loop at the pins <= 3 nH (LAYOUT).
