vectivolt/PCM/hardware/PCS-PWR-4W/sheets/04_legb.kicad_sch

## KiCad design hardware/PCS-PWR-4W/sheets/04_legb.kicad_sch (2026-10-07)

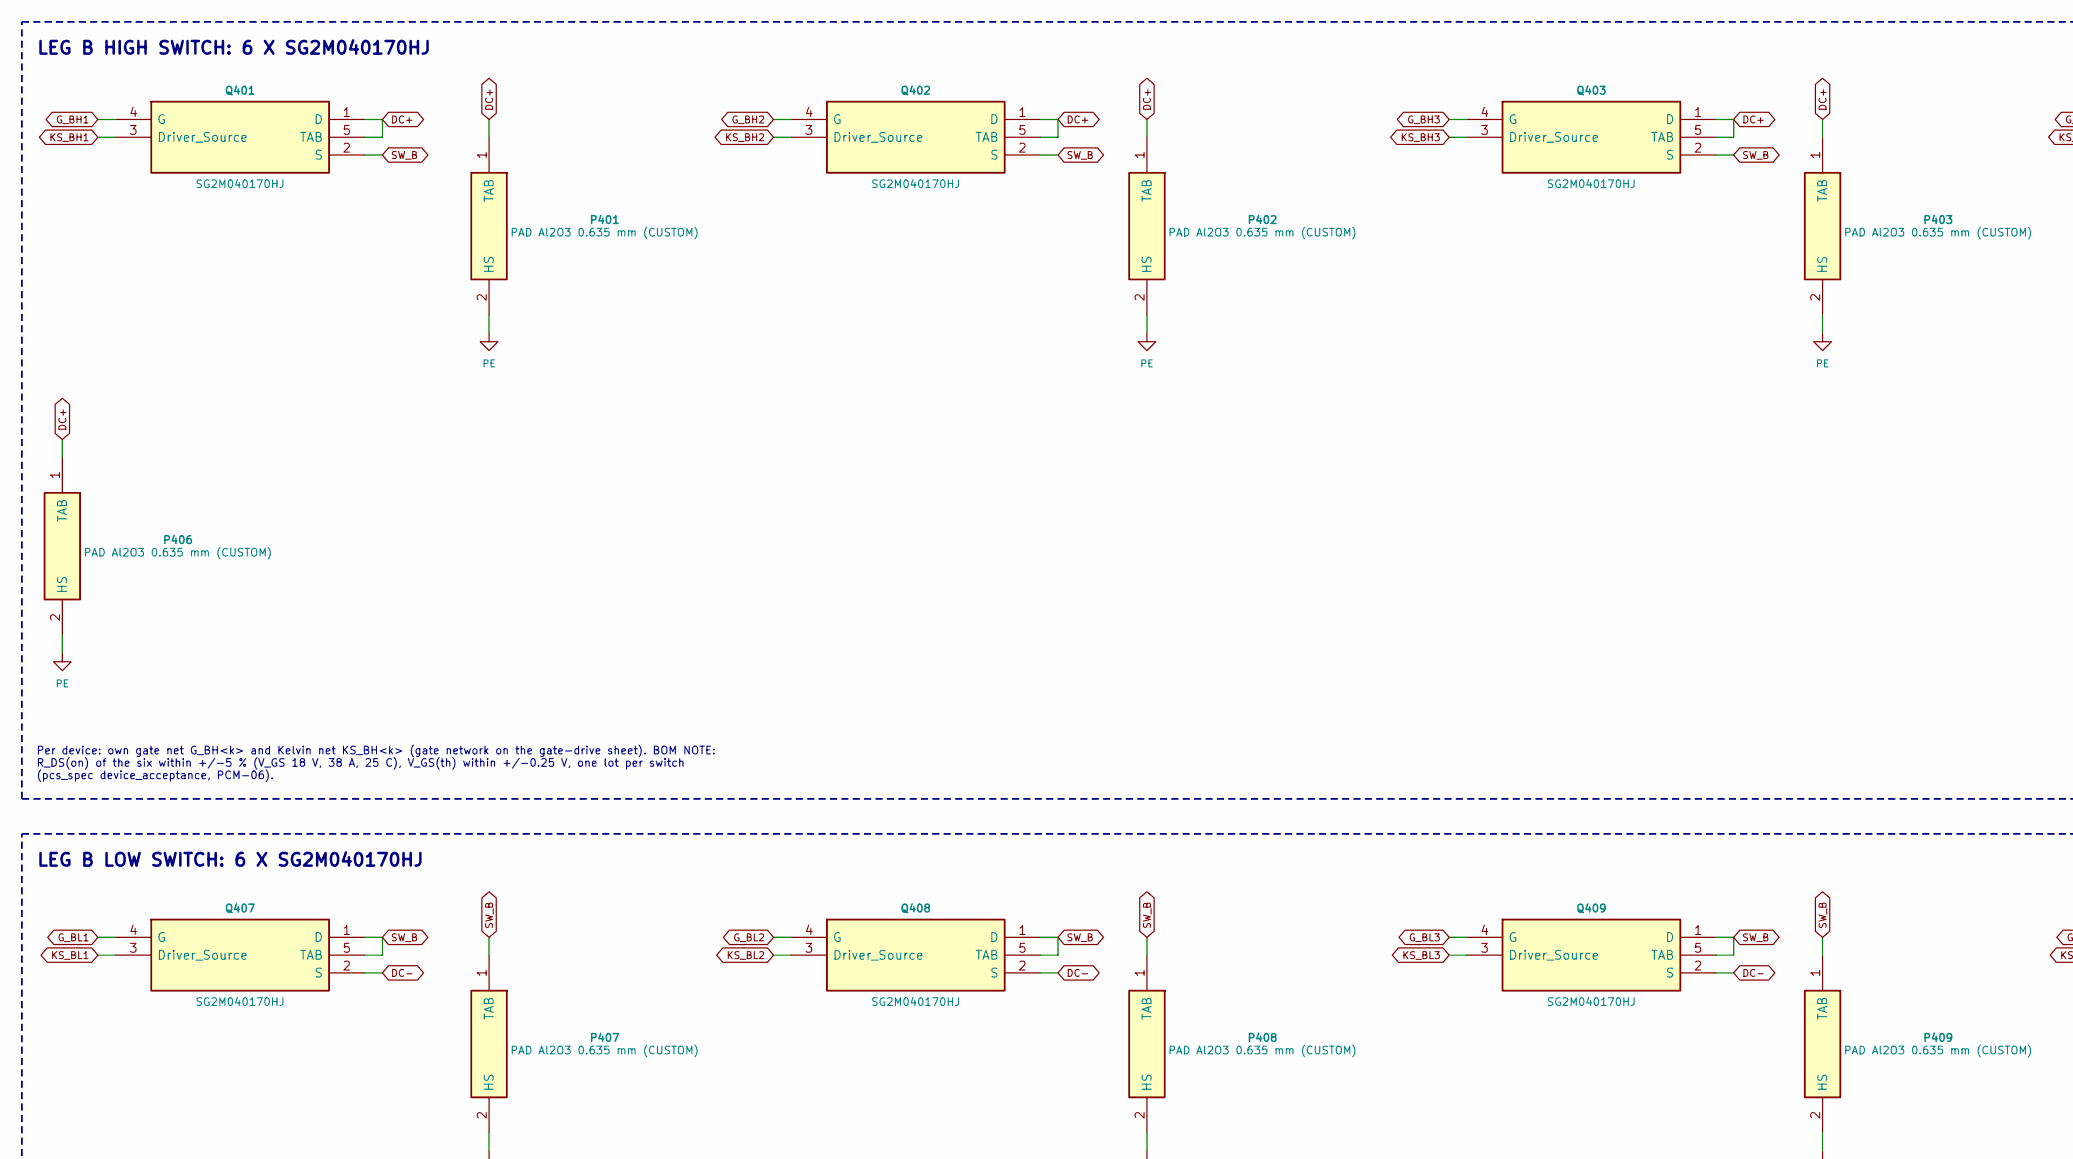
[picture p295: schematic 04_legb.kicad_sch, part in row 1, column 1]

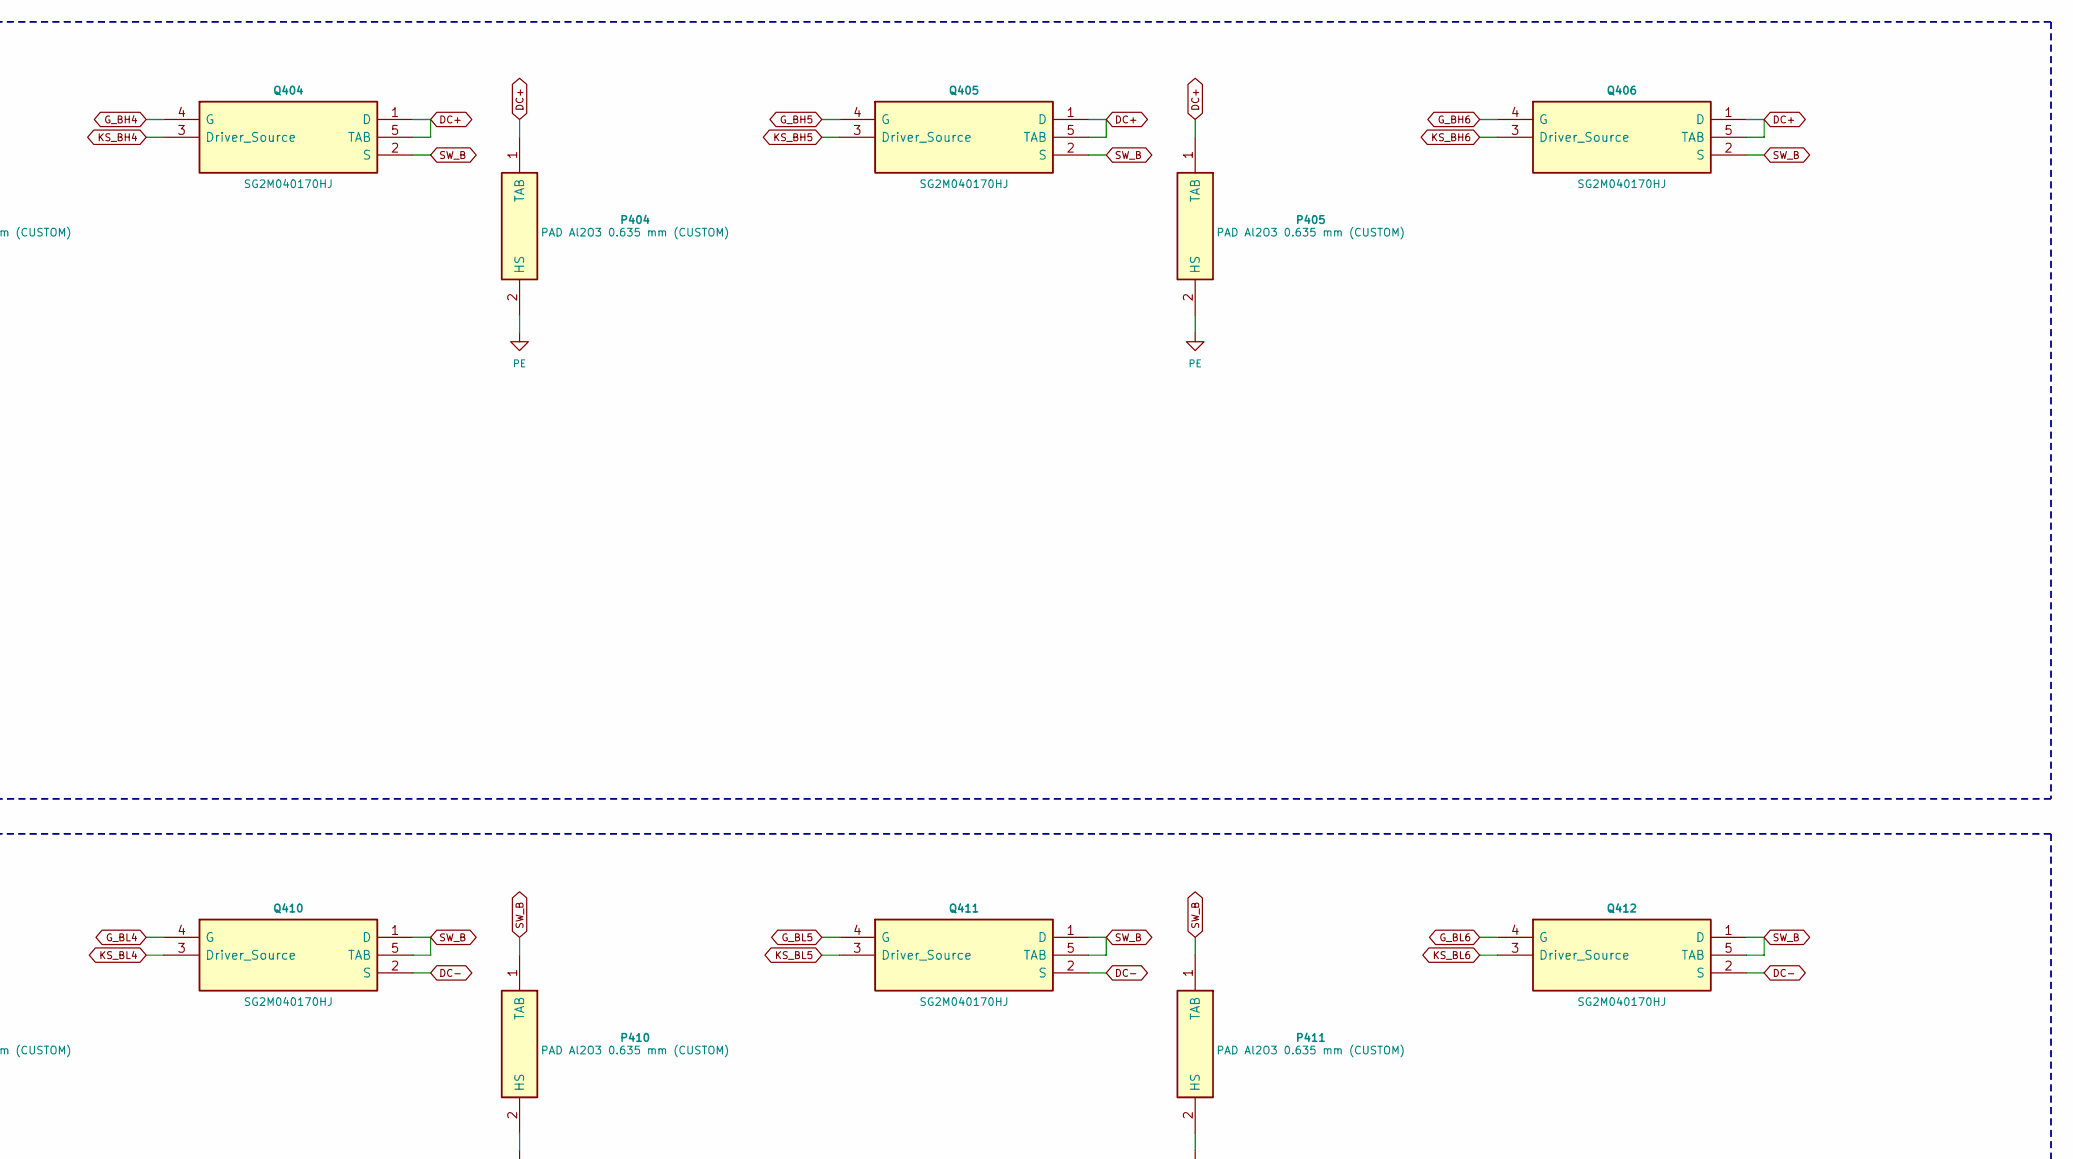
[picture p296: schematic 04_legb.kicad_sch, part in row 1, column 2]

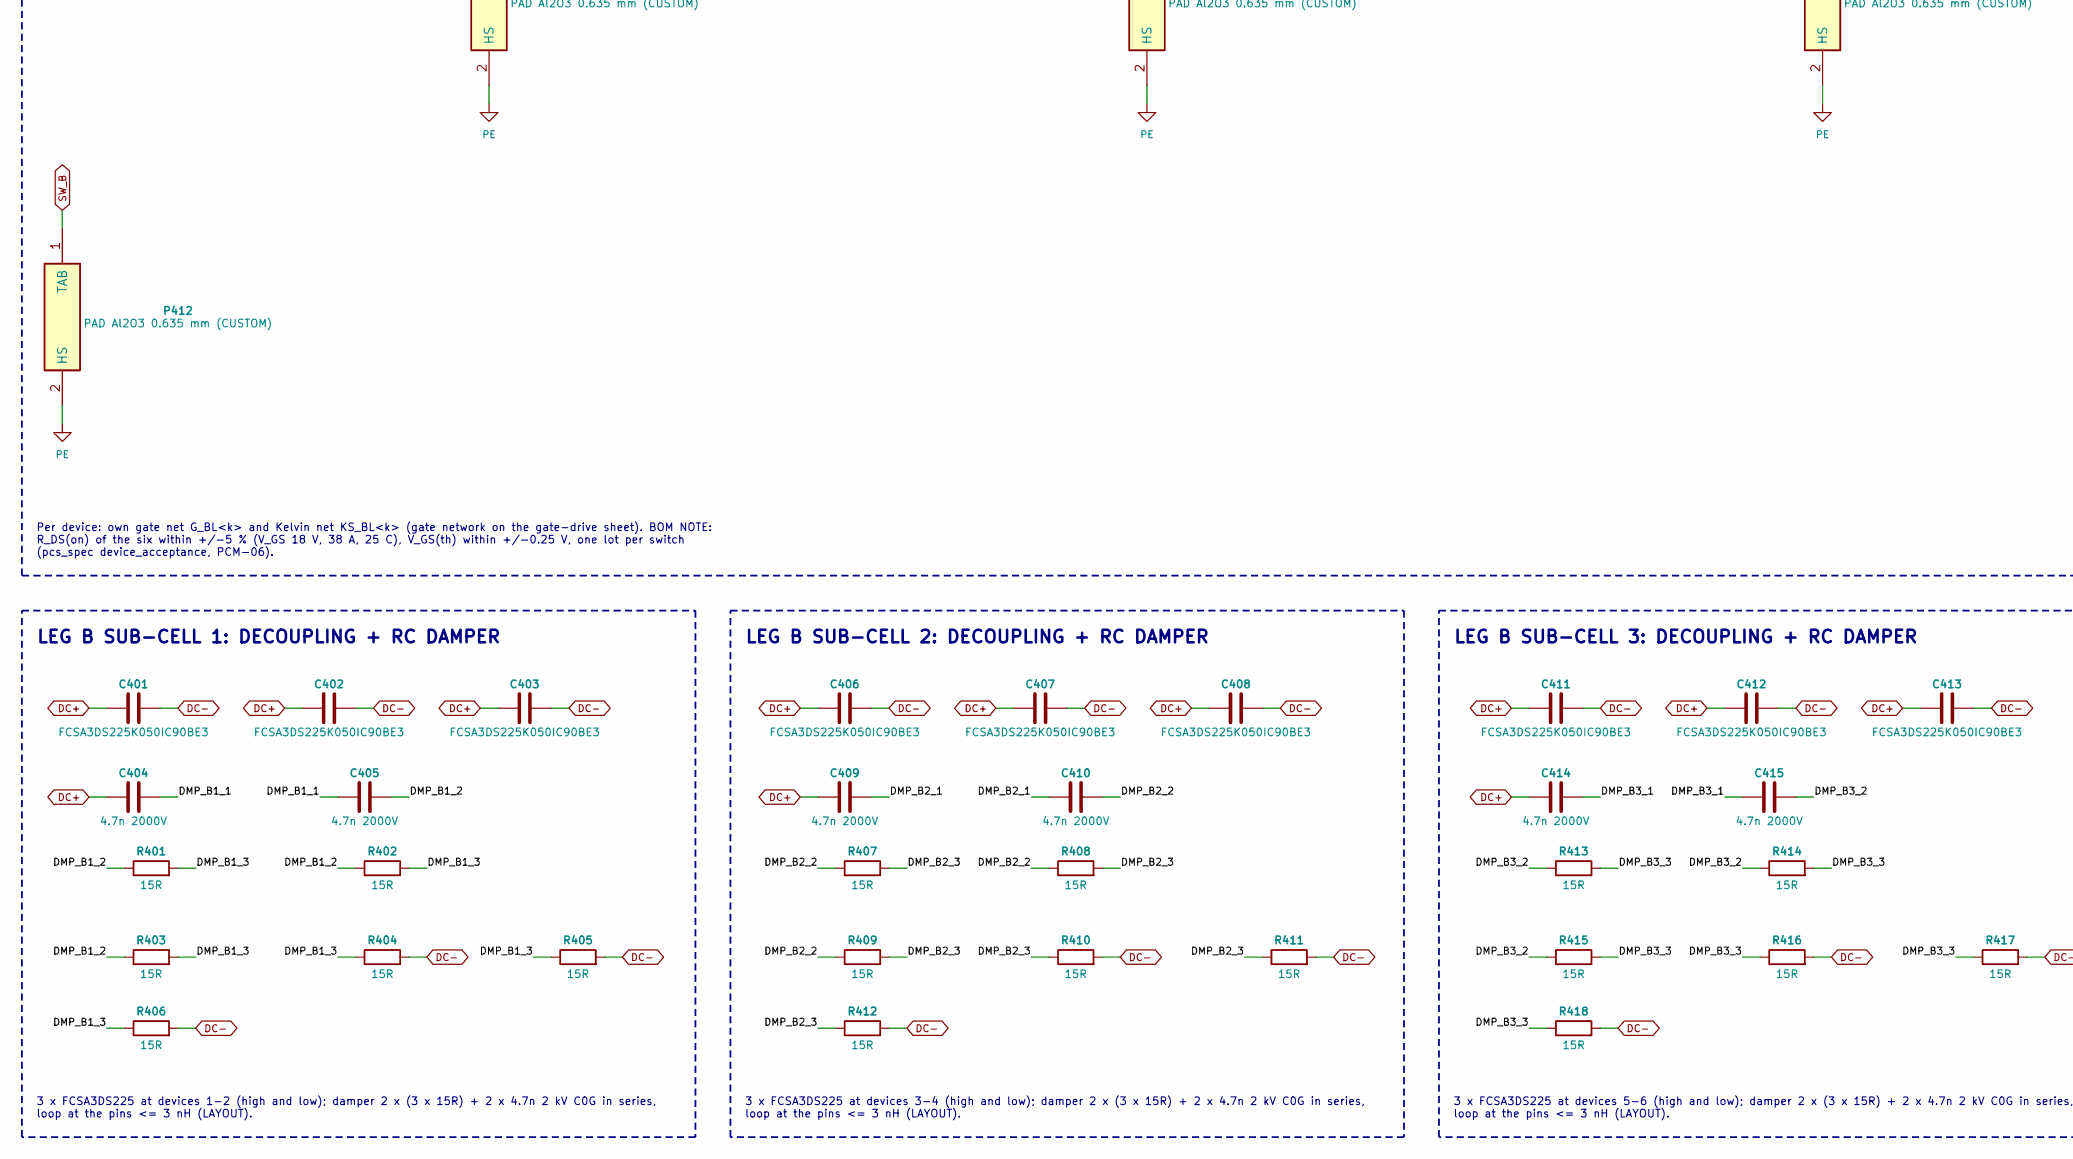
[picture p297: schematic 04_legb.kicad_sch, part in row 2, column 1]

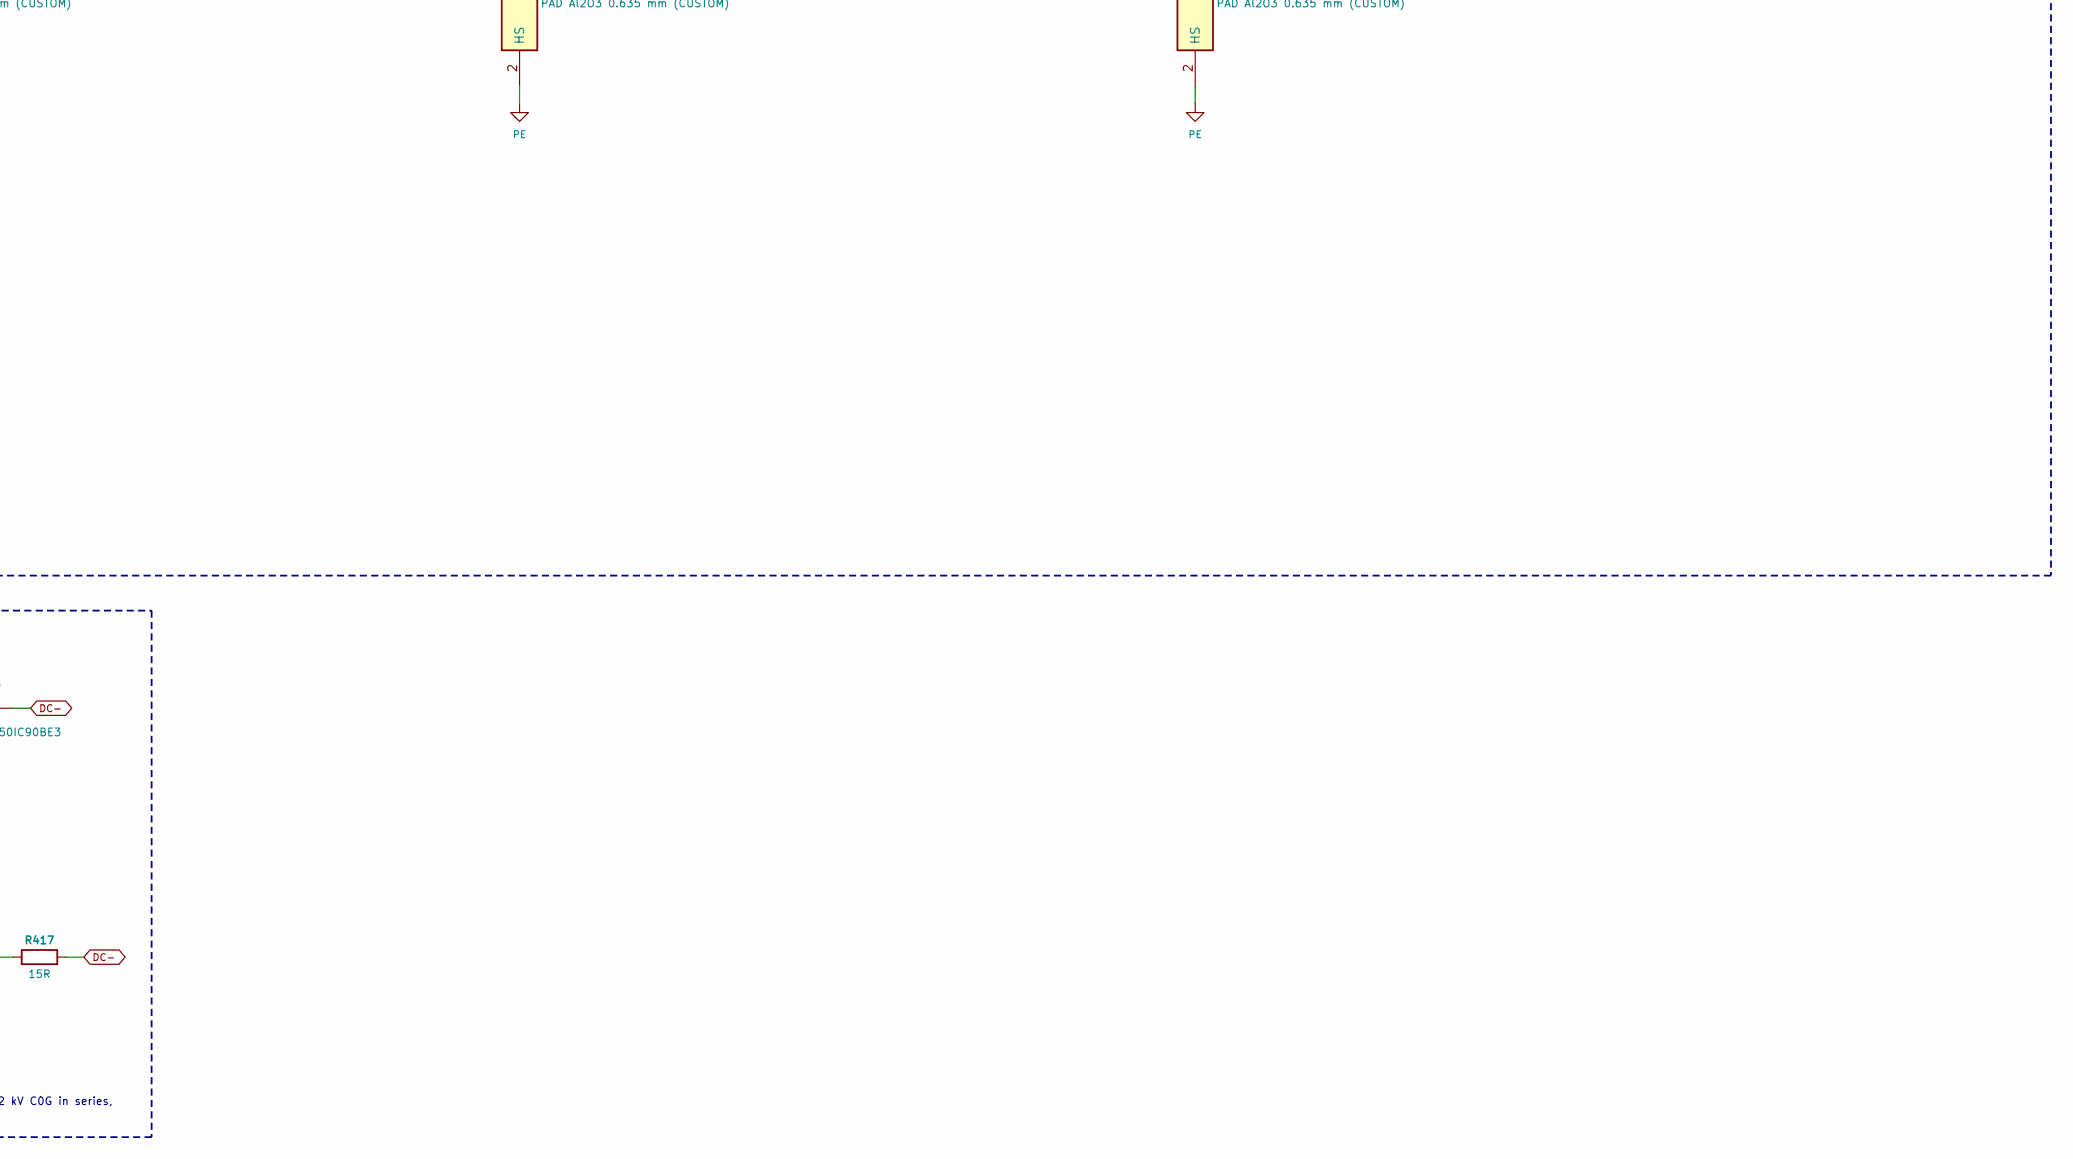
[picture p298: schematic 04_legb.kicad_sch, part in row 2, column 2]

Parts:
C401, C402, C403, C406, C407, C408, C411, C412, C413: FCSA3DS225K050IC90BE3; MPN FCSA3DS225K050IC90BE3
C404, C405, C409, C410, C414, C415: 4.7n 2000V
P401, P402, P403, P404, P405, P406, P407, P408, P409, P410, P411, P412: PAD Al2O3 0.635 mm (CUSTOM)
Q401, Q402, Q403, Q404, Q405, Q406, Q407, Q408, Q409, Q410, Q411, Q412: SG2M040170HJ; MPN SG2M040170HJ
R401, R402, R403, R404, R405, R406, R407, R408, R409, R410, R411, R412, R413, R414, R415, R416, R417, R418: 15R; MPN CRCW251215R0FKEGHP

Connections:
DC+: C401.1, C402.1, C403.1, C404.1, C406.1, C407.1, C408.1, C409.1, C411.1, C412.1, C413.1, C414.1, P401.1 (TAB), P402.1 (TAB), P403.1 (TAB), P404.1 (TAB), P405.1 (TAB), P406.1 (TAB), Q401.1 (D), Q401.5 (TAB), Q402.1 (D), Q402.5 (TAB), Q403.1 (D), Q403.5 (TAB), Q404.1 (D), Q404.5 (TAB), Q405.1 (D), Q405.5 (TAB), Q406.1 (D), Q406.5 (TAB)
DC-: C401.2, C402.2, C403.2, C406.2, C407.2, C408.2, C411.2, C412.2, C413.2, Q407.2 (S), Q408.2 (S), Q409.2 (S), Q410.2 (S), Q411.2 (S), Q412.2 (S), R404.2, R405.2, R406.2, R410.2, R411.2, R412.2, R416.2, R417.2, R418.2
DMP_B1_1: C404.2, C405.1
DMP_B1_2: C405.2, R401.1, R402.1, R403.1
DMP_B1_3: R401.2, R402.2, R403.2, R404.1, R405.1, R406.1
DMP_B2_1: C409.2, C410.1
DMP_B2_2: C410.2, R407.1, R408.1, R409.1
DMP_B2_3: R407.2, R408.2, R409.2, R410.1, R411.1, R412.1
DMP_B3_1: C414.2, C415.1
DMP_B3_2: C415.2, R413.1, R414.1, R415.1
DMP_B3_3: R413.2, R414.2, R415.2, R416.1, R417.1, R418.1
G_BH1: Q401.4 (G)
G_BH2: Q402.4 (G)
G_BH3: Q403.4 (G)
G_BH4: Q404.4 (G)
G_BH5: Q405.4 (G)
G_BH6: Q406.4 (G)
G_BL1: Q407.4 (G)
G_BL2: Q408.4 (G)
G_BL3: Q409.4 (G)
G_BL4: Q410.4 (G)
G_BL5: Q411.4 (G)
G_BL6: Q412.4 (G)
KS_BH1: Q401.3 (Driver_Source)
KS_BH2: Q402.3 (Driver_Source)
KS_BH3: Q403.3 (Driver_Source)
KS_BH4: Q404.3 (Driver_Source)
KS_BH5: Q405.3 (Driver_Source)
KS_BH6: Q406.3 (Driver_Source)
KS_BL1: Q407.3 (Driver_Source)
KS_BL2: Q408.3 (Driver_Source)
KS_BL3: Q409.3 (Driver_Source)
KS_BL4: Q410.3 (Driver_Source)
KS_BL5: Q411.3 (Driver_Source)
KS_BL6: Q412.3 (Driver_Source)
PE: P401.2 (HS), P402.2 (HS), P403.2 (HS), P404.2 (HS), P405.2 (HS), P406.2 (HS), P407.2 (HS), P408.2 (HS), P409.2 (HS), P410.2 (HS), P411.2 (HS), P412.2 (HS)
SW_B: P407.1 (TAB), P408.1 (TAB), P409.1 (TAB), P410.1 (TAB), P411.1 (TAB), P412.1 (TAB), Q401.2 (S), Q402.2 (S), Q403.2 (S), Q404.2 (S), Q405.2 (S), Q406.2 (S), Q407.1 (D), Q407.5 (TAB), Q408.1 (D), Q408.5 (TAB), Q409.1 (D), Q409.5 (TAB), Q410.1 (D), Q410.5 (TAB), Q411.1 (D), Q411.5 (TAB), Q412.1 (D), Q412.5 (TAB)

Notes on the sheet:
Per device: own gate net G_BH<k> and Kelvin net KS_BH<k> (gate network on the gate-drive sheet). BOM NOTE: R_DS(on) of the six within +/-5 % (V_GS 18 V, 38 A, 25 C), V_GS(th) within +/-0.25 V, one lot per switch (pcs_spec device_acceptance, PCM-06).
3 x FCSA3DS225 at devices 1-2 (high and low); damper 2 x (3 x 15R) + 2 x 4.7n 2 kV C0G in series, loop at the pins <= 3 nH (LAYOUT).
LEG B SUB-CELL 2: DECOUPLING + RC DAMPER
Per device: own gate net G_BL<k> and Kelvin net KS_BL<k> (gate network on the gate-drive sheet). BOM NOTE: R_DS(on) of the six within +/-5 % (V_GS 18 V, 38 A, 25 C), V_GS(th) within +/-0.25 V, one lot per switch (pcs_spec device_acceptance, PCM-06).
3 x FCSA3DS225 at devices 5-6 (high and low); damper 2 x (3 x 15R) + 2 x 4.7n 2 kV C0G in series, loop at the pins <= 3 nH (LAYOUT).
3 x FCSA3DS225 at devices 3-4 (high and low); damper 2 x (3 x 15R) + 2 x 4.7n 2 kV C0G in series, loop at the pins <= 3 nH (LAYOUT).
LEG B SUB-CELL 1: DECOUPLING + RC DAMPER
LEG B HIGH SWITCH: 6 X SG2M040170HJ
LEG B SUB-CELL 3: DECOUPLING + RC DAMPER
LEG B LOW SWITCH: 6 X SG2M040170HJ
