vectivolt/PCM/hardware/PCS-PWR-4W/sheets/05_legc.kicad_sch

## KiCad design hardware/PCS-PWR-4W/sheets/05_legc.kicad_sch (2026-10-07)

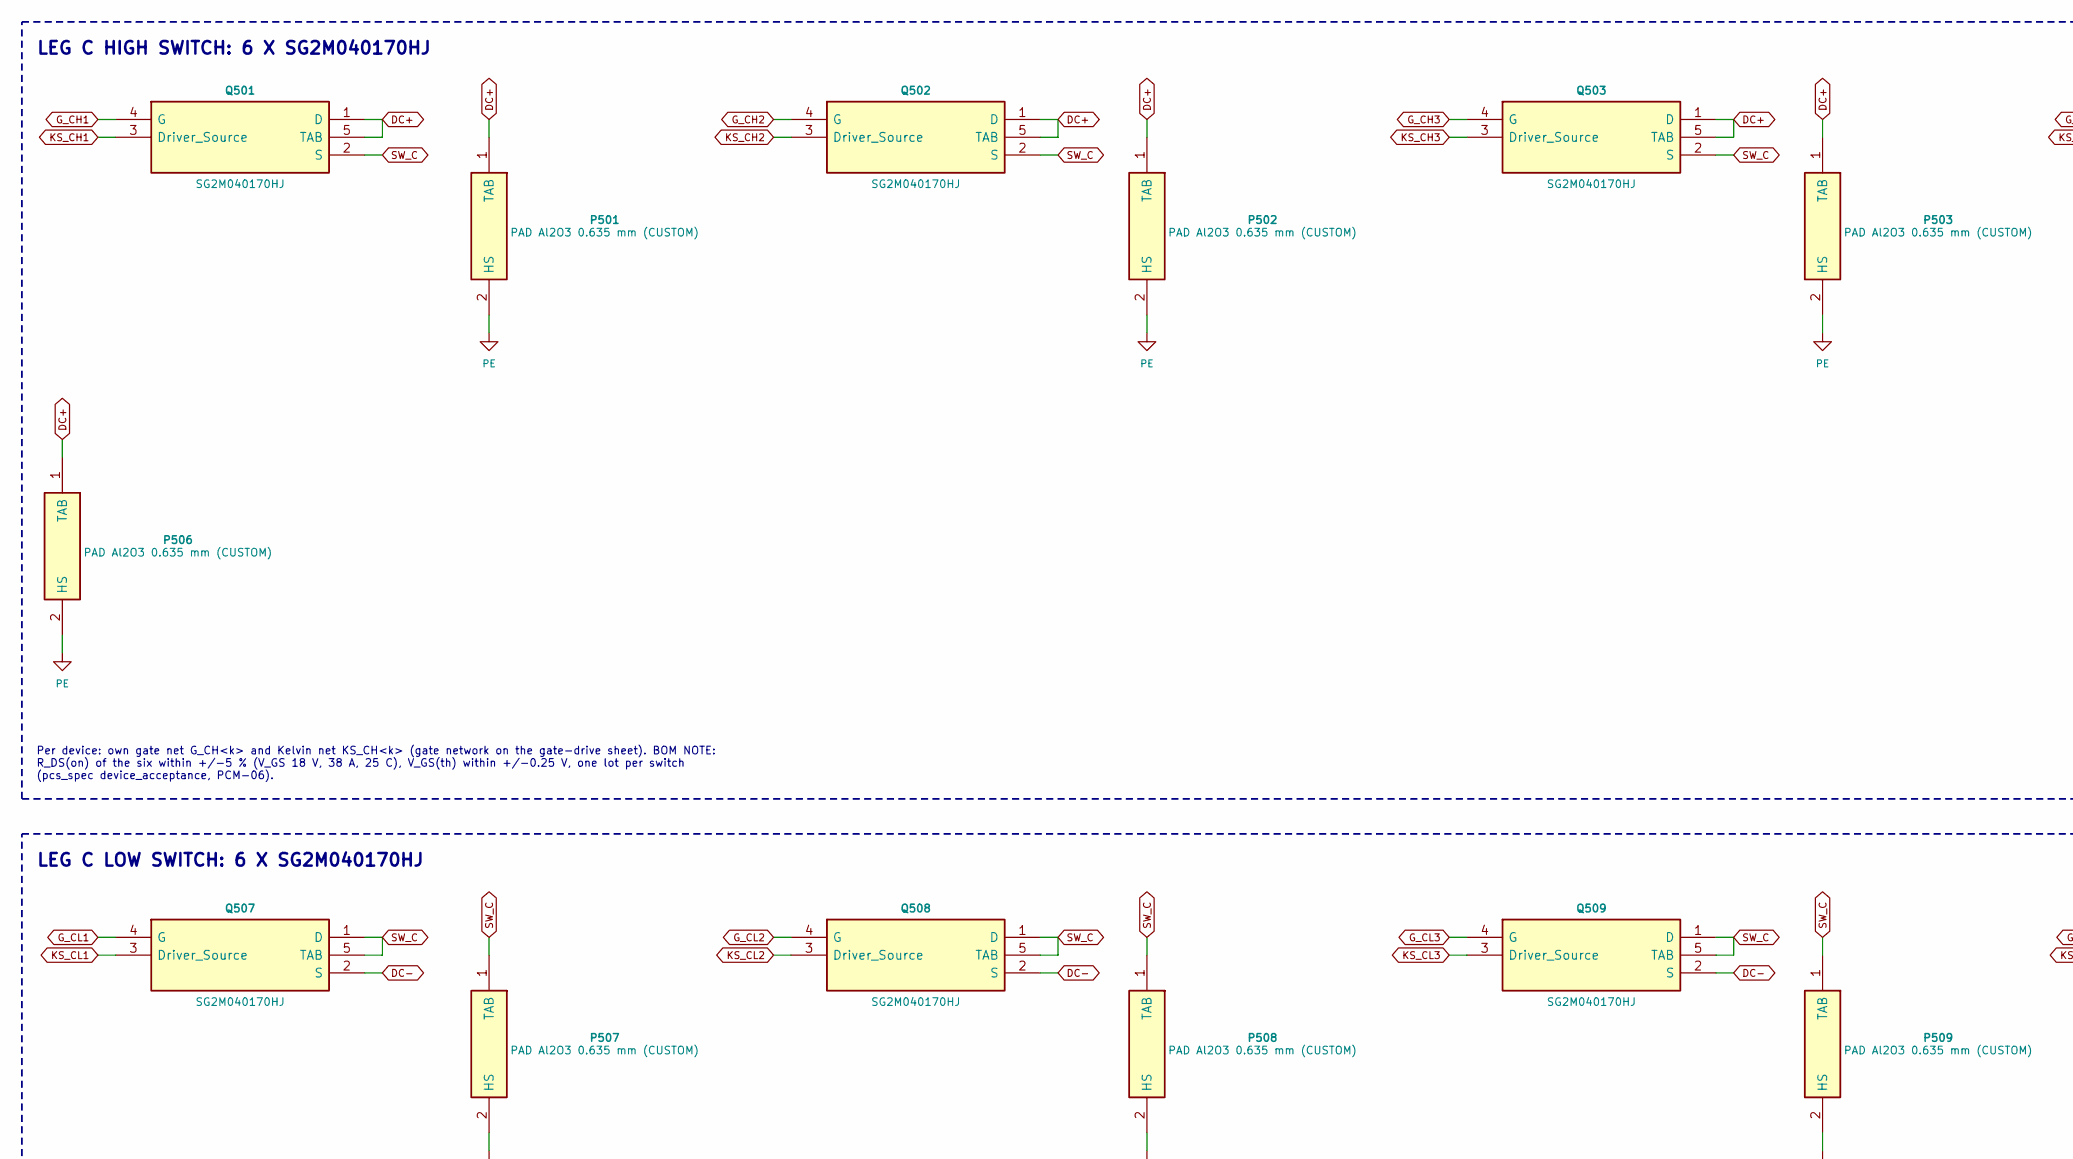
[picture p299: schematic 05_legc.kicad_sch, part in row 1, column 1]

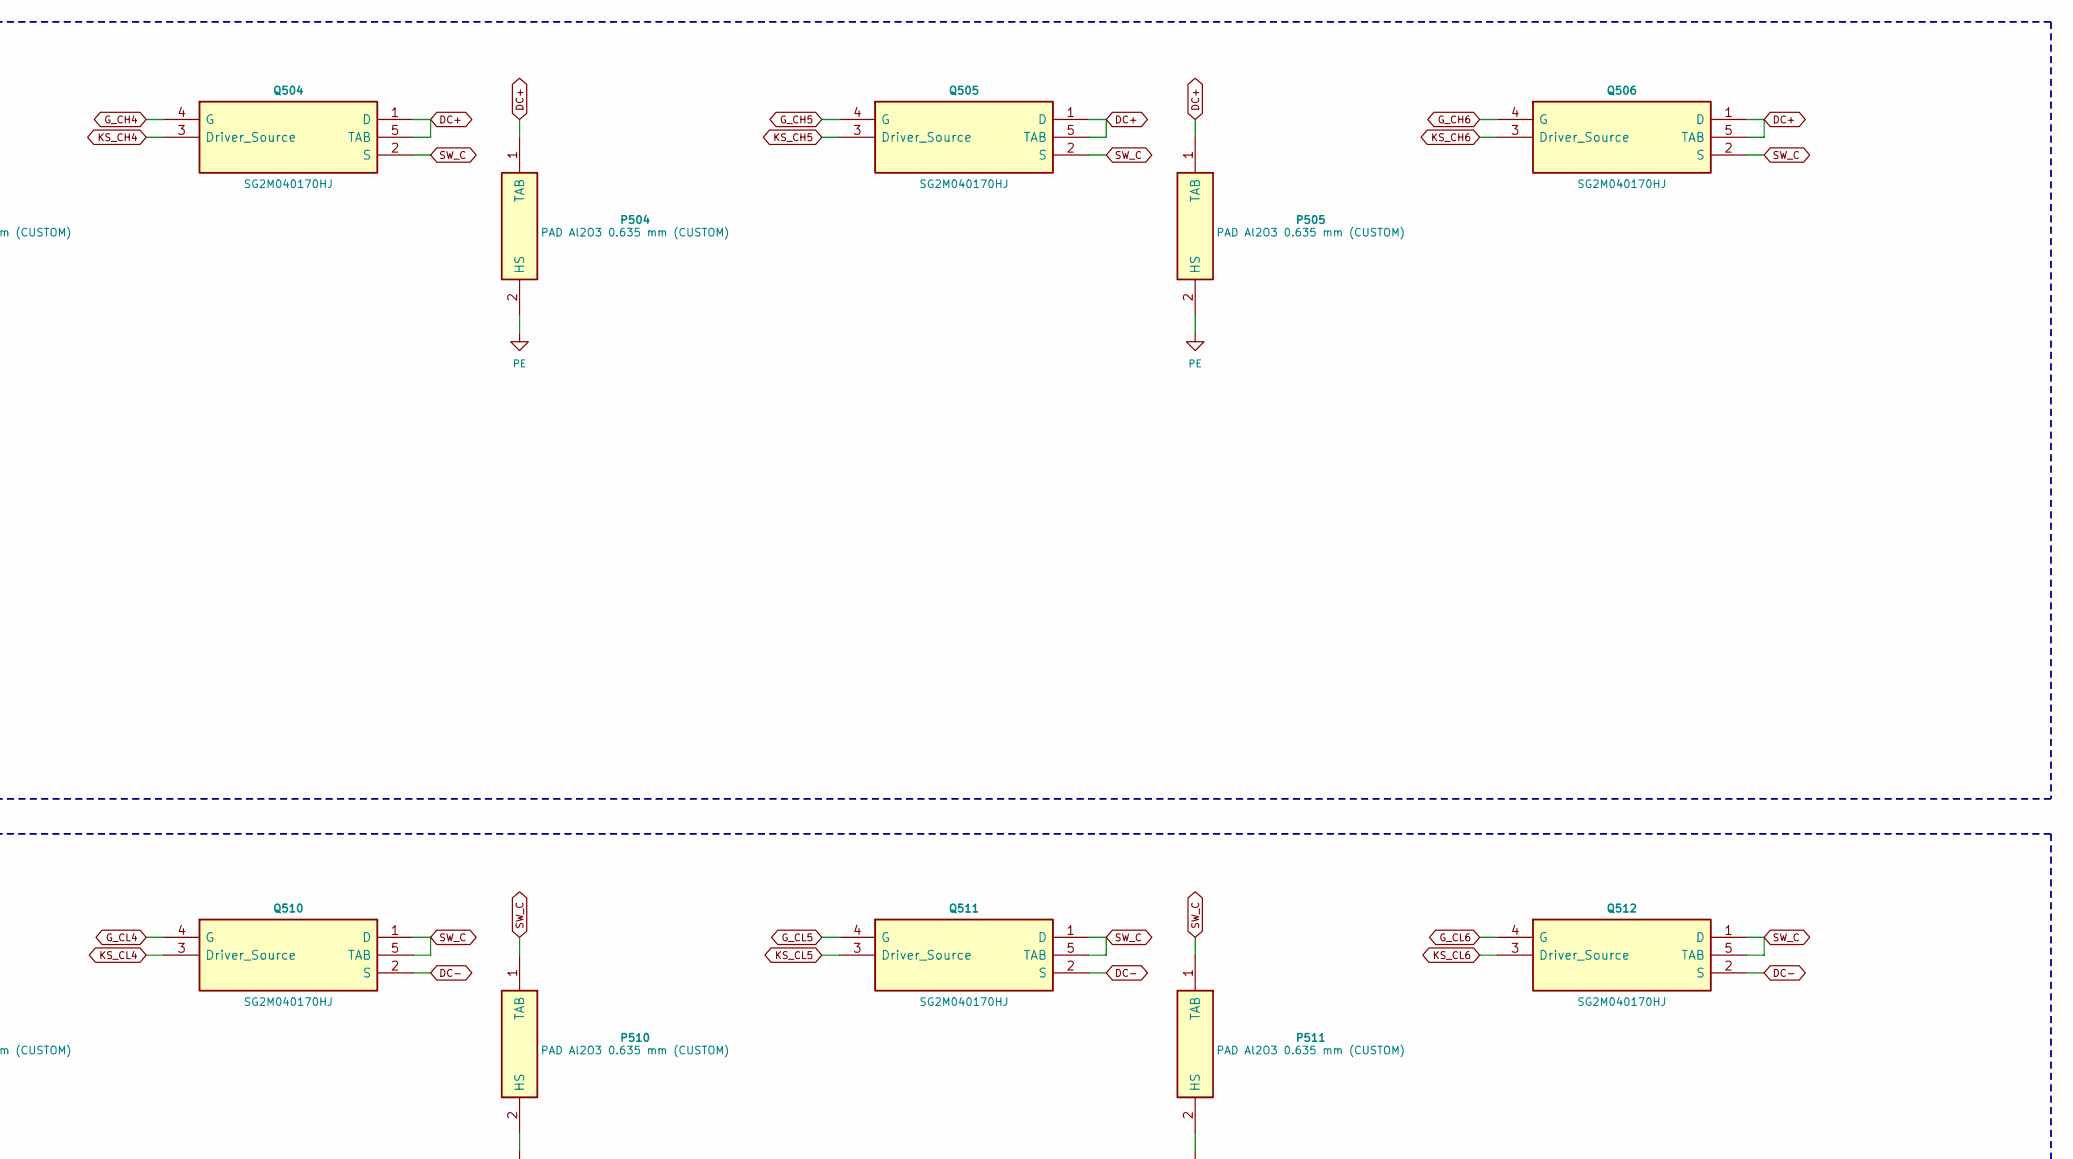
[picture p300: schematic 05_legc.kicad_sch, part in row 1, column 2]

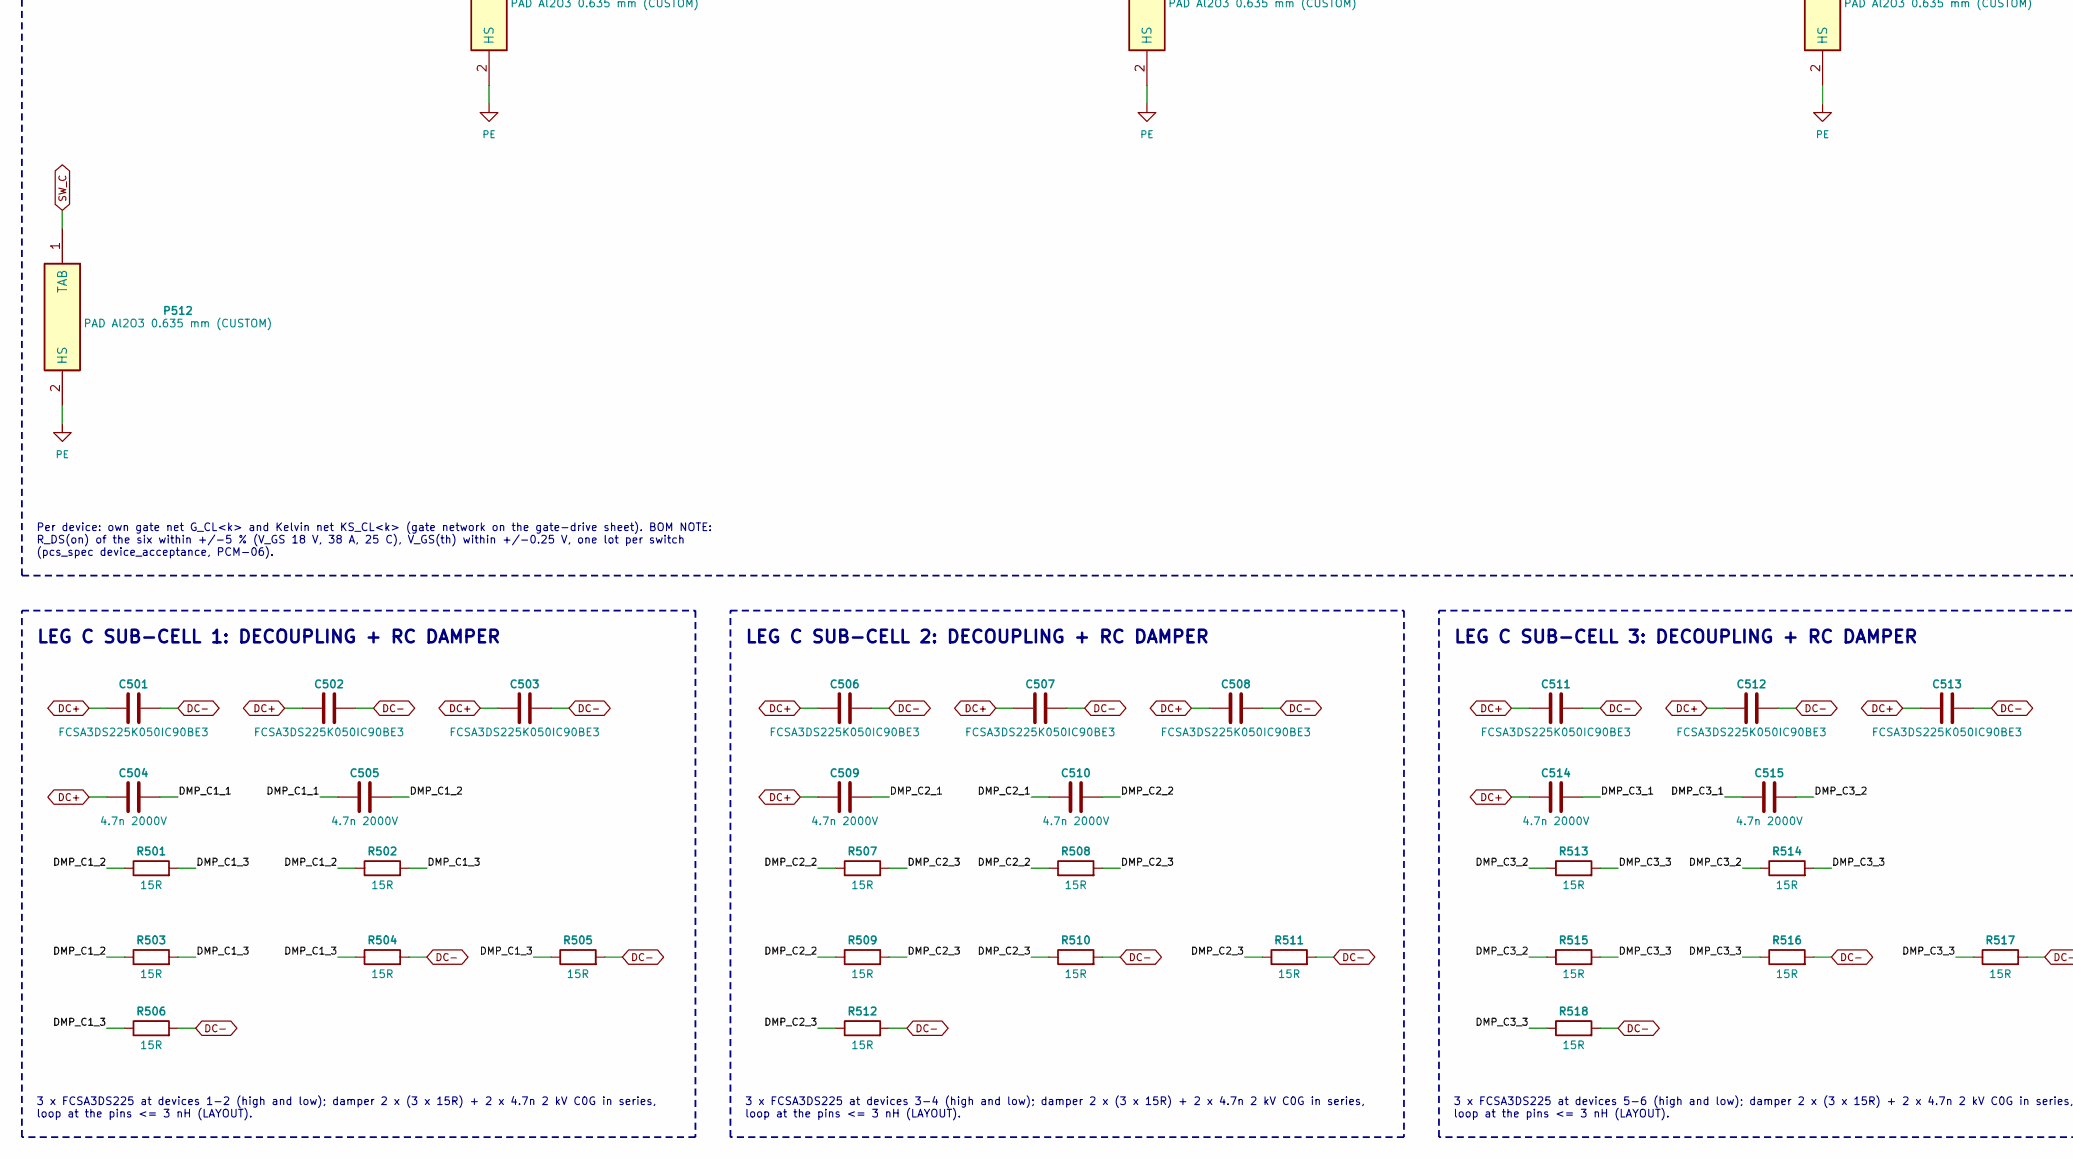
[picture p301: schematic 05_legc.kicad_sch, part in row 2, column 1]

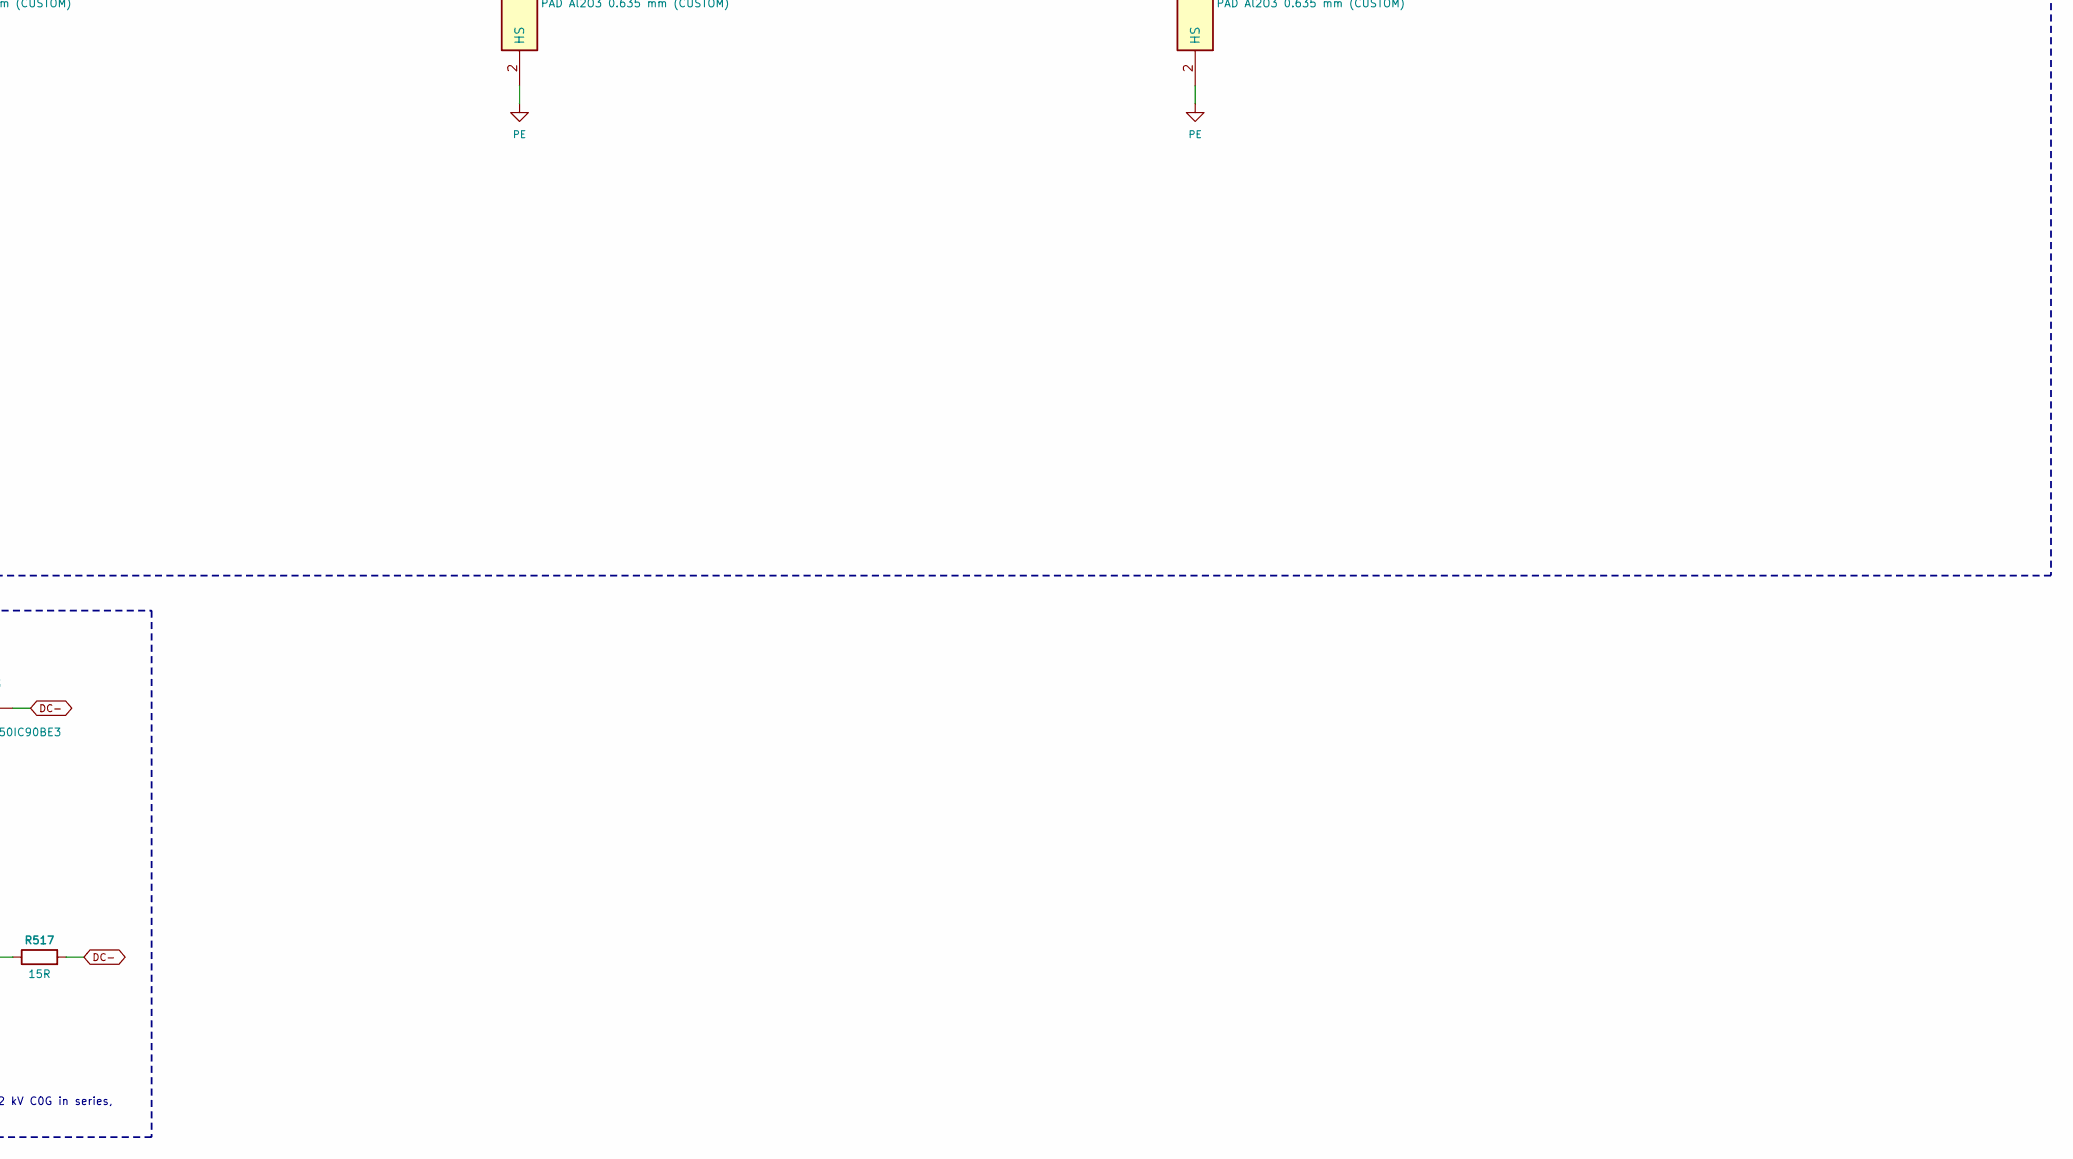
[picture p302: schematic 05_legc.kicad_sch, part in row 2, column 2]

Parts:
C501, C502, C503, C506, C507, C508, C511, C512, C513: FCSA3DS225K050IC90BE3; MPN FCSA3DS225K050IC90BE3
C504, C505, C509, C510, C514, C515: 4.7n 2000V
P501, P502, P503, P504, P505, P506, P507, P508, P509, P510, P511, P512: PAD Al2O3 0.635 mm (CUSTOM)
Q501, Q502, Q503, Q504, Q505, Q506, Q507, Q508, Q509, Q510, Q511, Q512: SG2M040170HJ; MPN SG2M040170HJ
R501, R502, R503, R504, R505, R506, R507, R508, R509, R510, R511, R512, R513, R514, R515, R516, R517, R518: 15R; MPN CRCW251215R0FKEGHP

Connections:
DC+: C501.1, C502.1, C503.1, C504.1, C506.1, C507.1, C508.1, C509.1, C511.1, C512.1, C513.1, C514.1, P501.1 (TAB), P502.1 (TAB), P503.1 (TAB), P504.1 (TAB), P505.1 (TAB), P506.1 (TAB), Q501.1 (D), Q501.5 (TAB), Q502.1 (D), Q502.5 (TAB), Q503.1 (D), Q503.5 (TAB), Q504.1 (D), Q504.5 (TAB), Q505.1 (D), Q505.5 (TAB), Q506.1 (D), Q506.5 (TAB)
DC-: C501.2, C502.2, C503.2, C506.2, C507.2, C508.2, C511.2, C512.2, C513.2, Q507.2 (S), Q508.2 (S), Q509.2 (S), Q510.2 (S), Q511.2 (S), Q512.2 (S), R504.2, R505.2, R506.2, R510.2, R511.2, R512.2, R516.2, R517.2, R518.2
DMP_C1_1: C504.2, C505.1
DMP_C1_2: C505.2, R501.1, R502.1, R503.1
DMP_C1_3: R501.2, R502.2, R503.2, R504.1, R505.1, R506.1
DMP_C2_1: C509.2, C510.1
DMP_C2_2: C510.2, R507.1, R508.1, R509.1
DMP_C2_3: R507.2, R508.2, R509.2, R510.1, R511.1, R512.1
DMP_C3_1: C514.2, C515.1
DMP_C3_2: C515.2, R513.1, R514.1, R515.1
DMP_C3_3: R513.2, R514.2, R515.2, R516.1, R517.1, R518.1
G_CH1: Q501.4 (G)
G_CH2: Q502.4 (G)
G_CH3: Q503.4 (G)
G_CH4: Q504.4 (G)
G_CH5: Q505.4 (G)
G_CH6: Q506.4 (G)
G_CL1: Q507.4 (G)
G_CL2: Q508.4 (G)
G_CL3: Q509.4 (G)
G_CL4: Q510.4 (G)
G_CL5: Q511.4 (G)
G_CL6: Q512.4 (G)
KS_CH1: Q501.3 (Driver_Source)
KS_CH2: Q502.3 (Driver_Source)
KS_CH3: Q503.3 (Driver_Source)
KS_CH4: Q504.3 (Driver_Source)
KS_CH5: Q505.3 (Driver_Source)
KS_CH6: Q506.3 (Driver_Source)
KS_CL1: Q507.3 (Driver_Source)
KS_CL2: Q508.3 (Driver_Source)
KS_CL3: Q509.3 (Driver_Source)
KS_CL4: Q510.3 (Driver_Source)
KS_CL5: Q511.3 (Driver_Source)
KS_CL6: Q512.3 (Driver_Source)
PE: P501.2 (HS), P502.2 (HS), P503.2 (HS), P504.2 (HS), P505.2 (HS), P506.2 (HS), P507.2 (HS), P508.2 (HS), P509.2 (HS), P510.2 (HS), P511.2 (HS), P512.2 (HS)
SW_C: P507.1 (TAB), P508.1 (TAB), P509.1 (TAB), P510.1 (TAB), P511.1 (TAB), P512.1 (TAB), Q501.2 (S), Q502.2 (S), Q503.2 (S), Q504.2 (S), Q505.2 (S), Q506.2 (S), Q507.1 (D), Q507.5 (TAB), Q508.1 (D), Q508.5 (TAB), Q509.1 (D), Q509.5 (TAB), Q510.1 (D), Q510.5 (TAB), Q511.1 (D), Q511.5 (TAB), Q512.1 (D), Q512.5 (TAB)

Notes on the sheet:
LEG C HIGH SWITCH: 6 X SG2M040170HJ
3 x FCSA3DS225 at devices 3-4 (high and low); damper 2 x (3 x 15R) + 2 x 4.7n 2 kV C0G in series, loop at the pins <= 3 nH (LAYOUT).
3 x FCSA3DS225 at devices 5-6 (high and low); damper 2 x (3 x 15R) + 2 x 4.7n 2 kV C0G in series, loop at the pins <= 3 nH (LAYOUT).
Per device: own gate net G_CH<k> and Kelvin net KS_CH<k> (gate network on the gate-drive sheet). BOM NOTE: R_DS(on) of the six within +/-5 % (V_GS 18 V, 38 A, 25 C), V_GS(th) within +/-0.25 V, one lot per switch (pcs_spec device_acceptance, PCM-06).
LEG C SUB-CELL 2: DECOUPLING + RC DAMPER
LEG C SUB-CELL 3: DECOUPLING + RC DAMPER
Per device: own gate net G_CL<k> and Kelvin net KS_CL<k> (gate network on the gate-drive sheet). BOM NOTE: R_DS(on) of the six within +/-5 % (V_GS 18 V, 38 A, 25 C), V_GS(th) within +/-0.25 V, one lot per switch (pcs_spec device_acceptance, PCM-06).
3 x FCSA3DS225 at devices 1-2 (high and low); damper 2 x (3 x 15R) + 2 x 4.7n 2 kV C0G in series, loop at the pins <= 3 nH (LAYOUT).
LEG C SUB-CELL 1: DECOUPLING + RC DAMPER
LEG C LOW SWITCH: 6 X SG2M040170HJ
