vectivolt/PCM/hardware/PCS-PWR-4W/sheets/06_legn.kicad_sch

## KiCad design hardware/PCS-PWR-4W/sheets/06_legn.kicad_sch (2026-10-07)

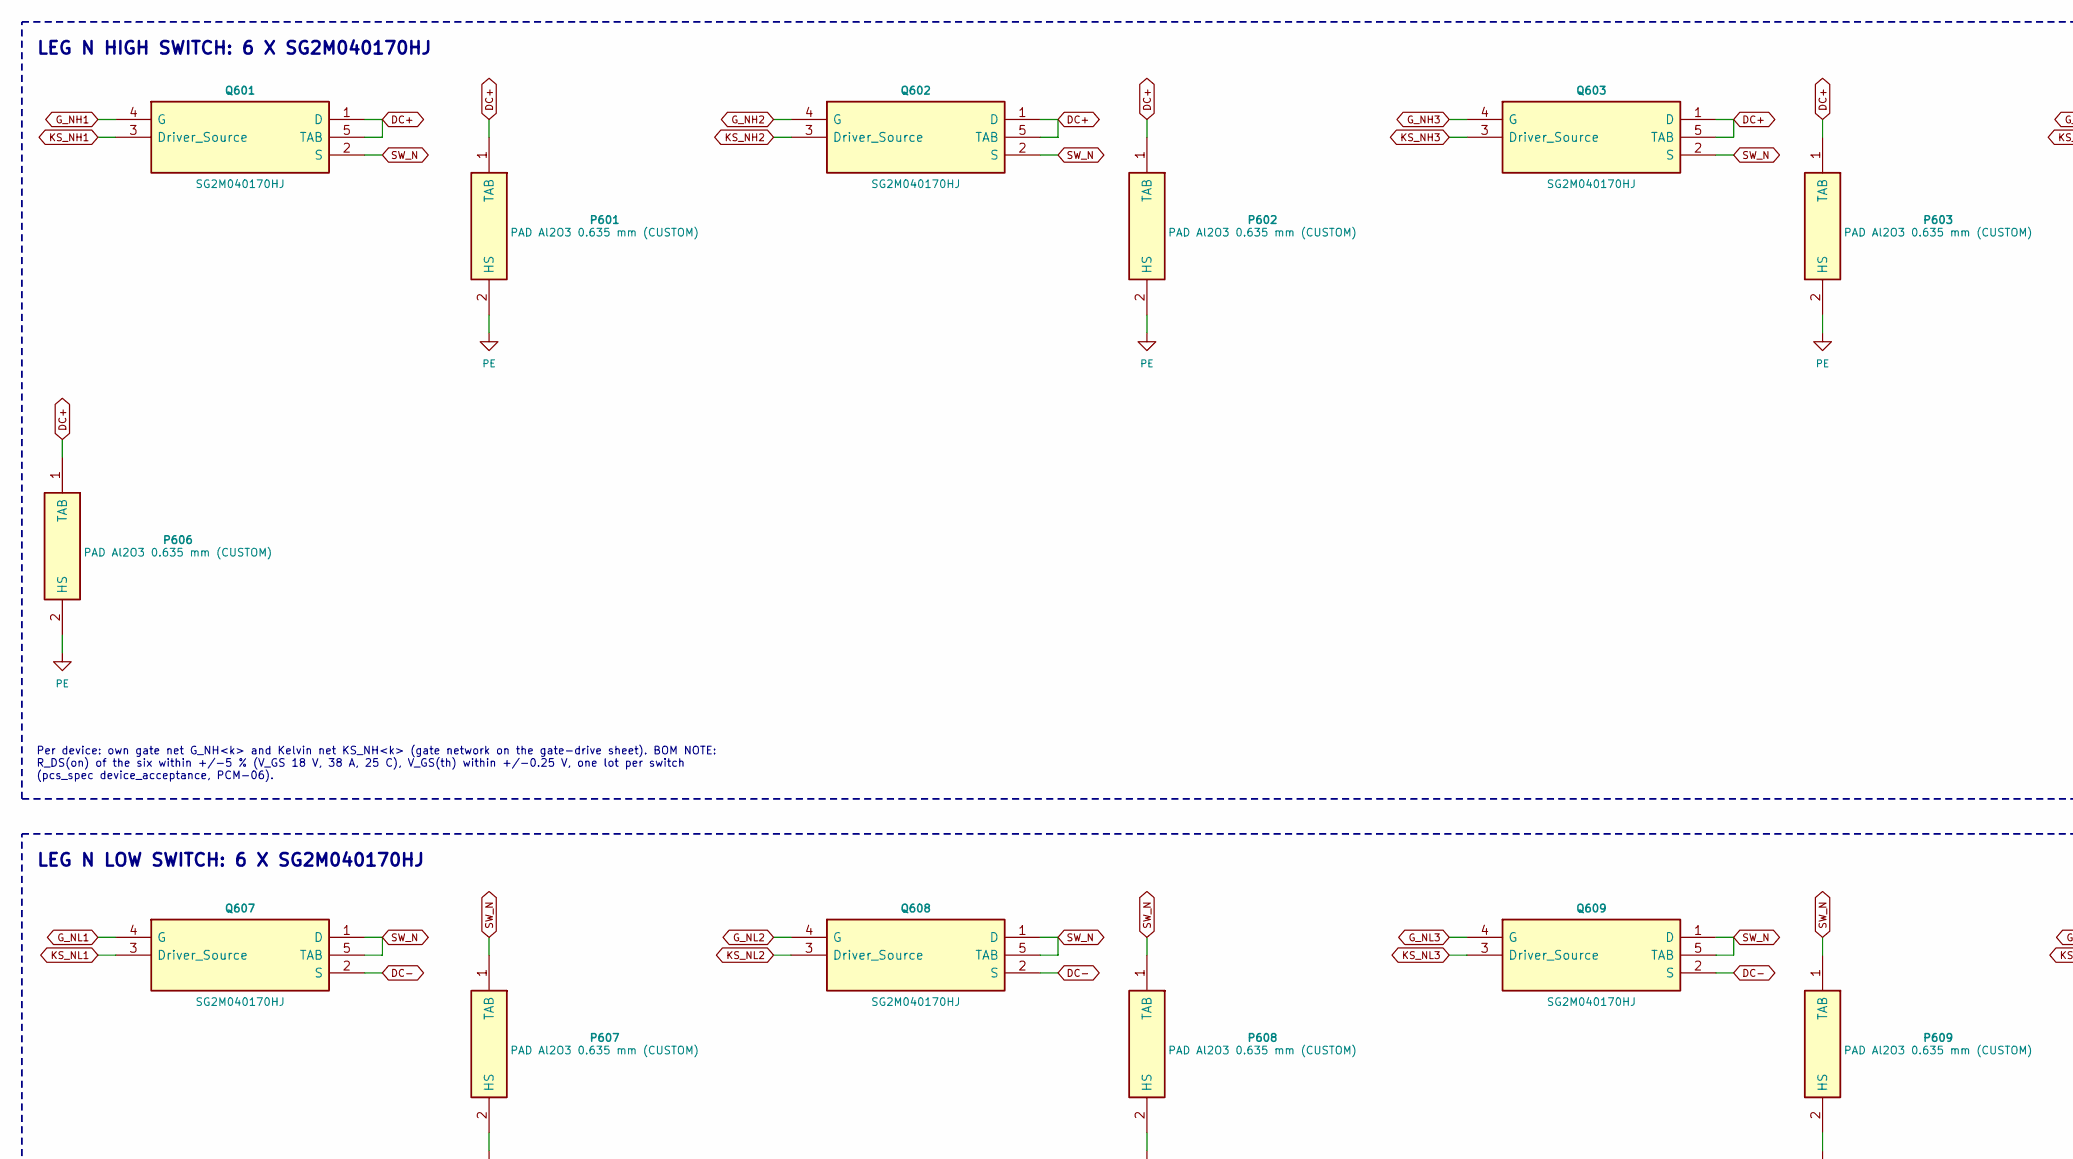
[picture p303: schematic 06_legn.kicad_sch, part in row 1, column 1]

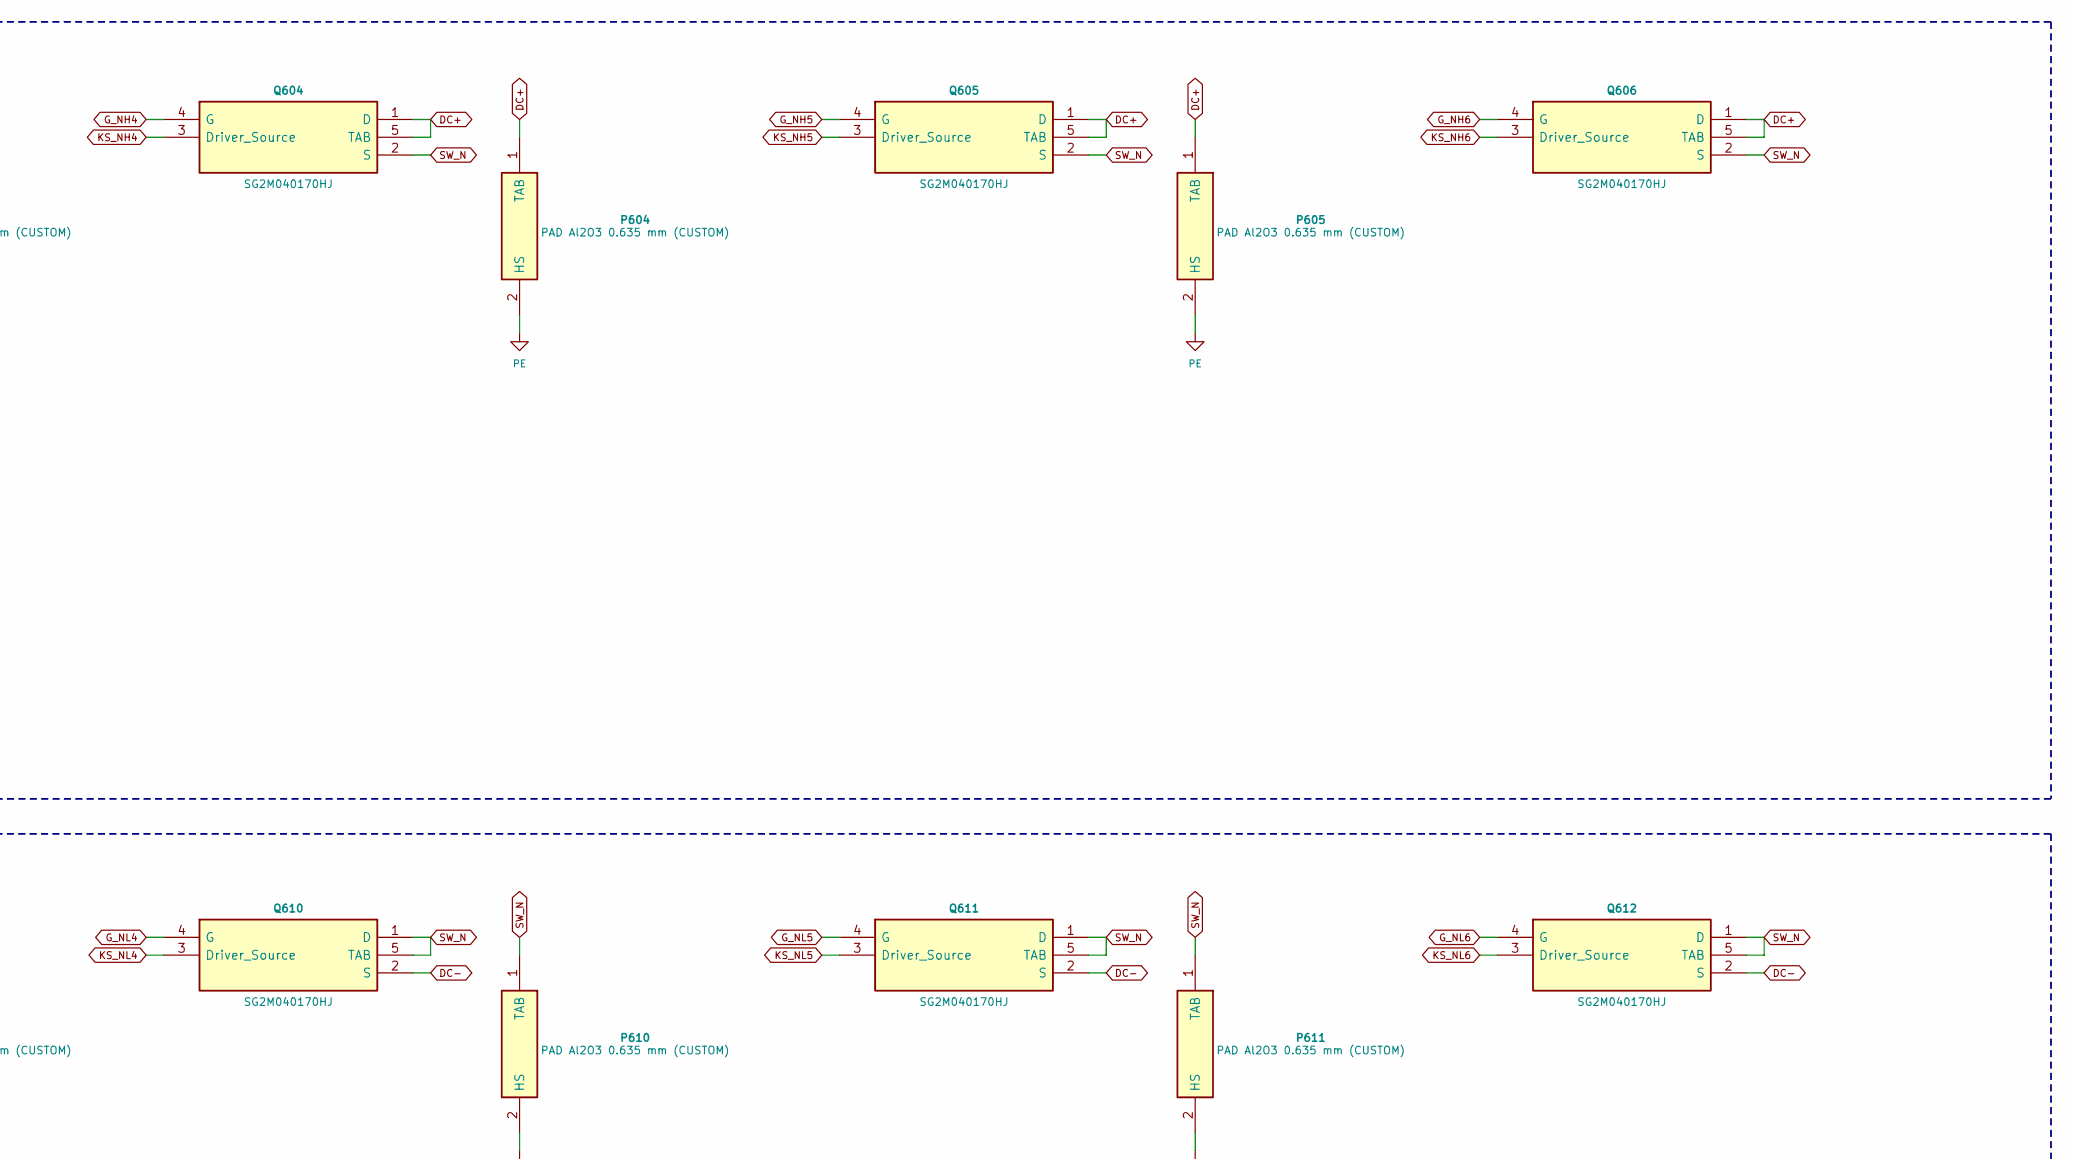
[picture p304: schematic 06_legn.kicad_sch, part in row 1, column 2]

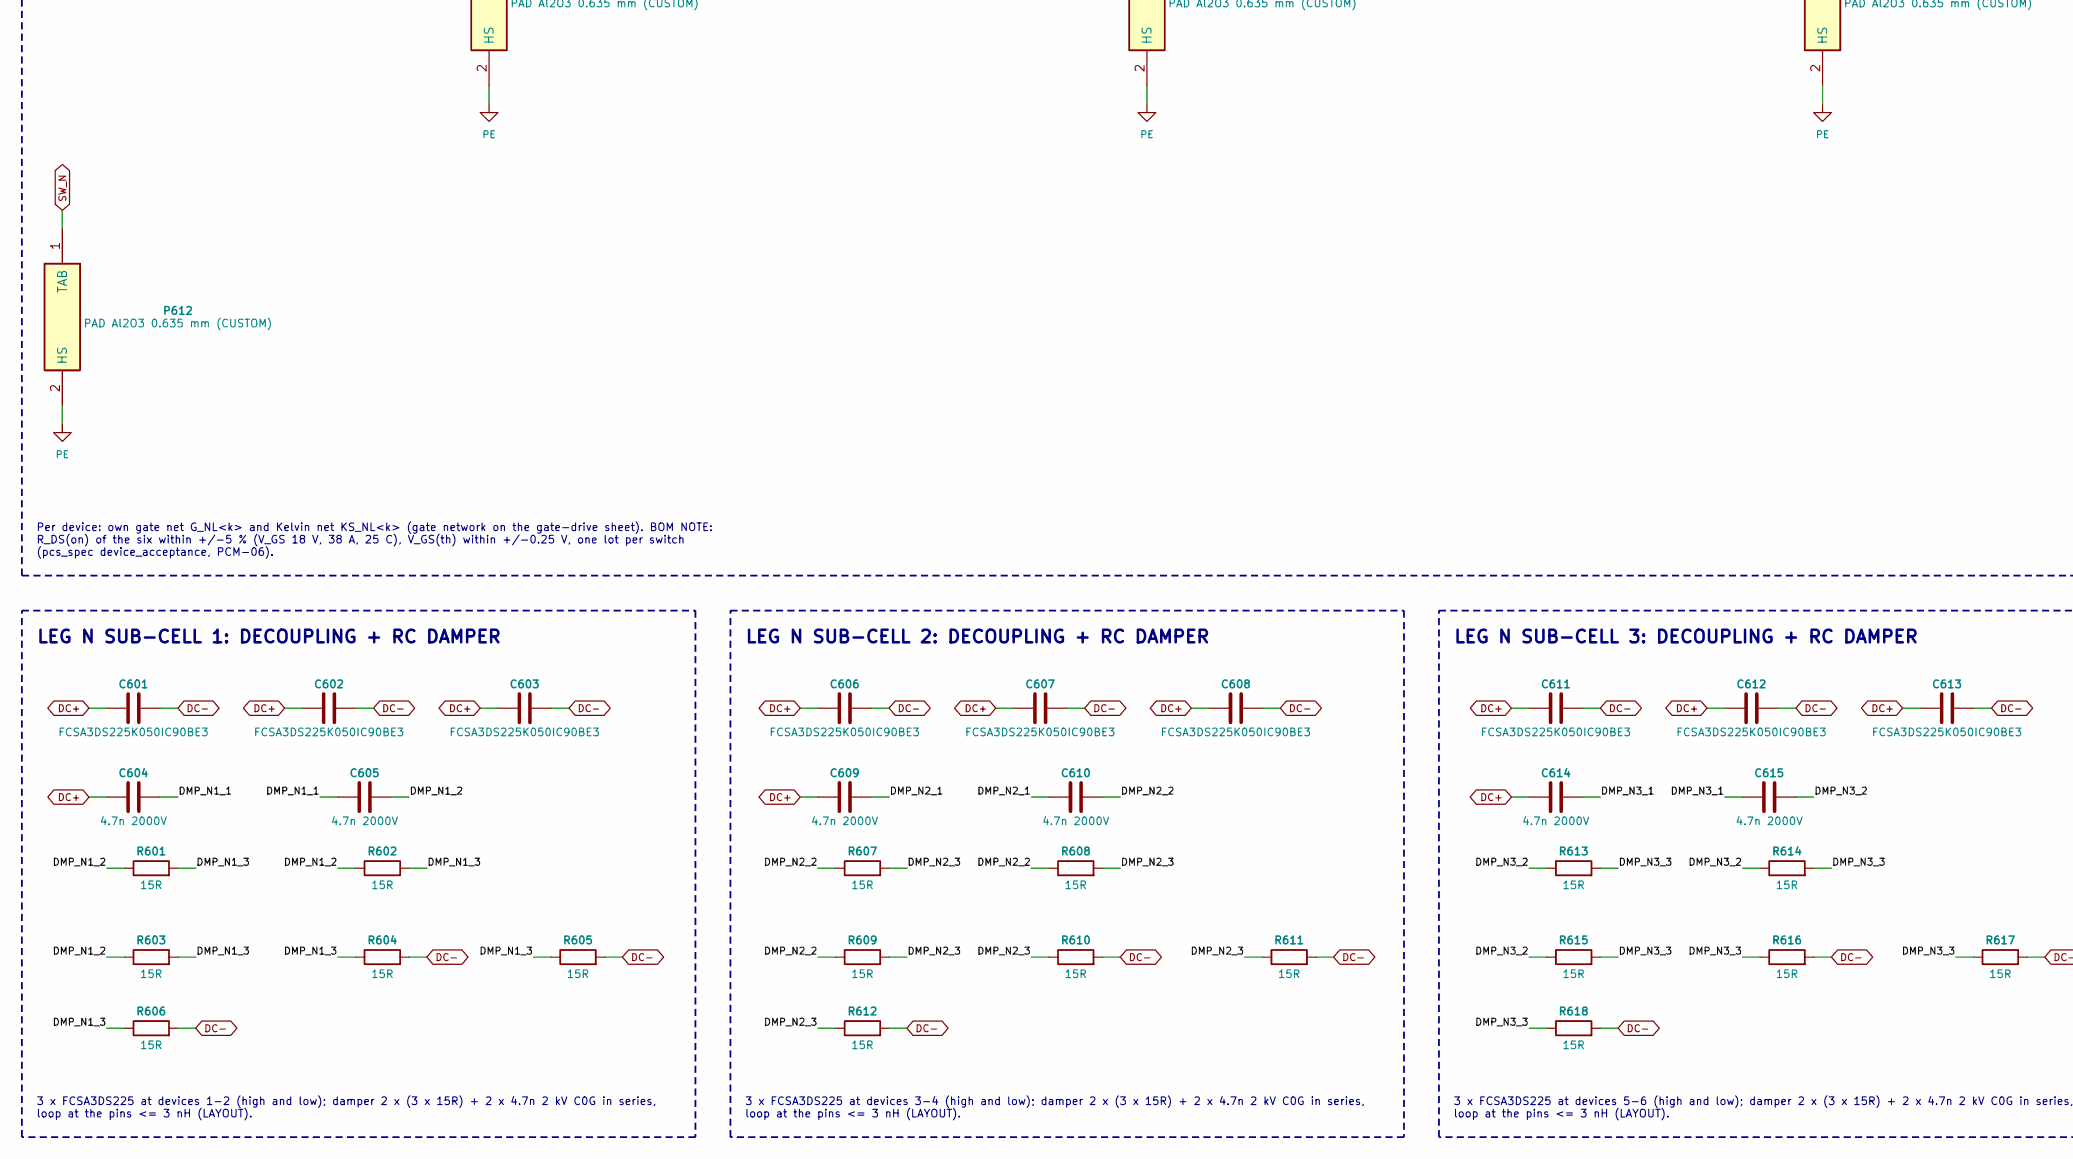
[picture p305: schematic 06_legn.kicad_sch, part in row 2, column 1]

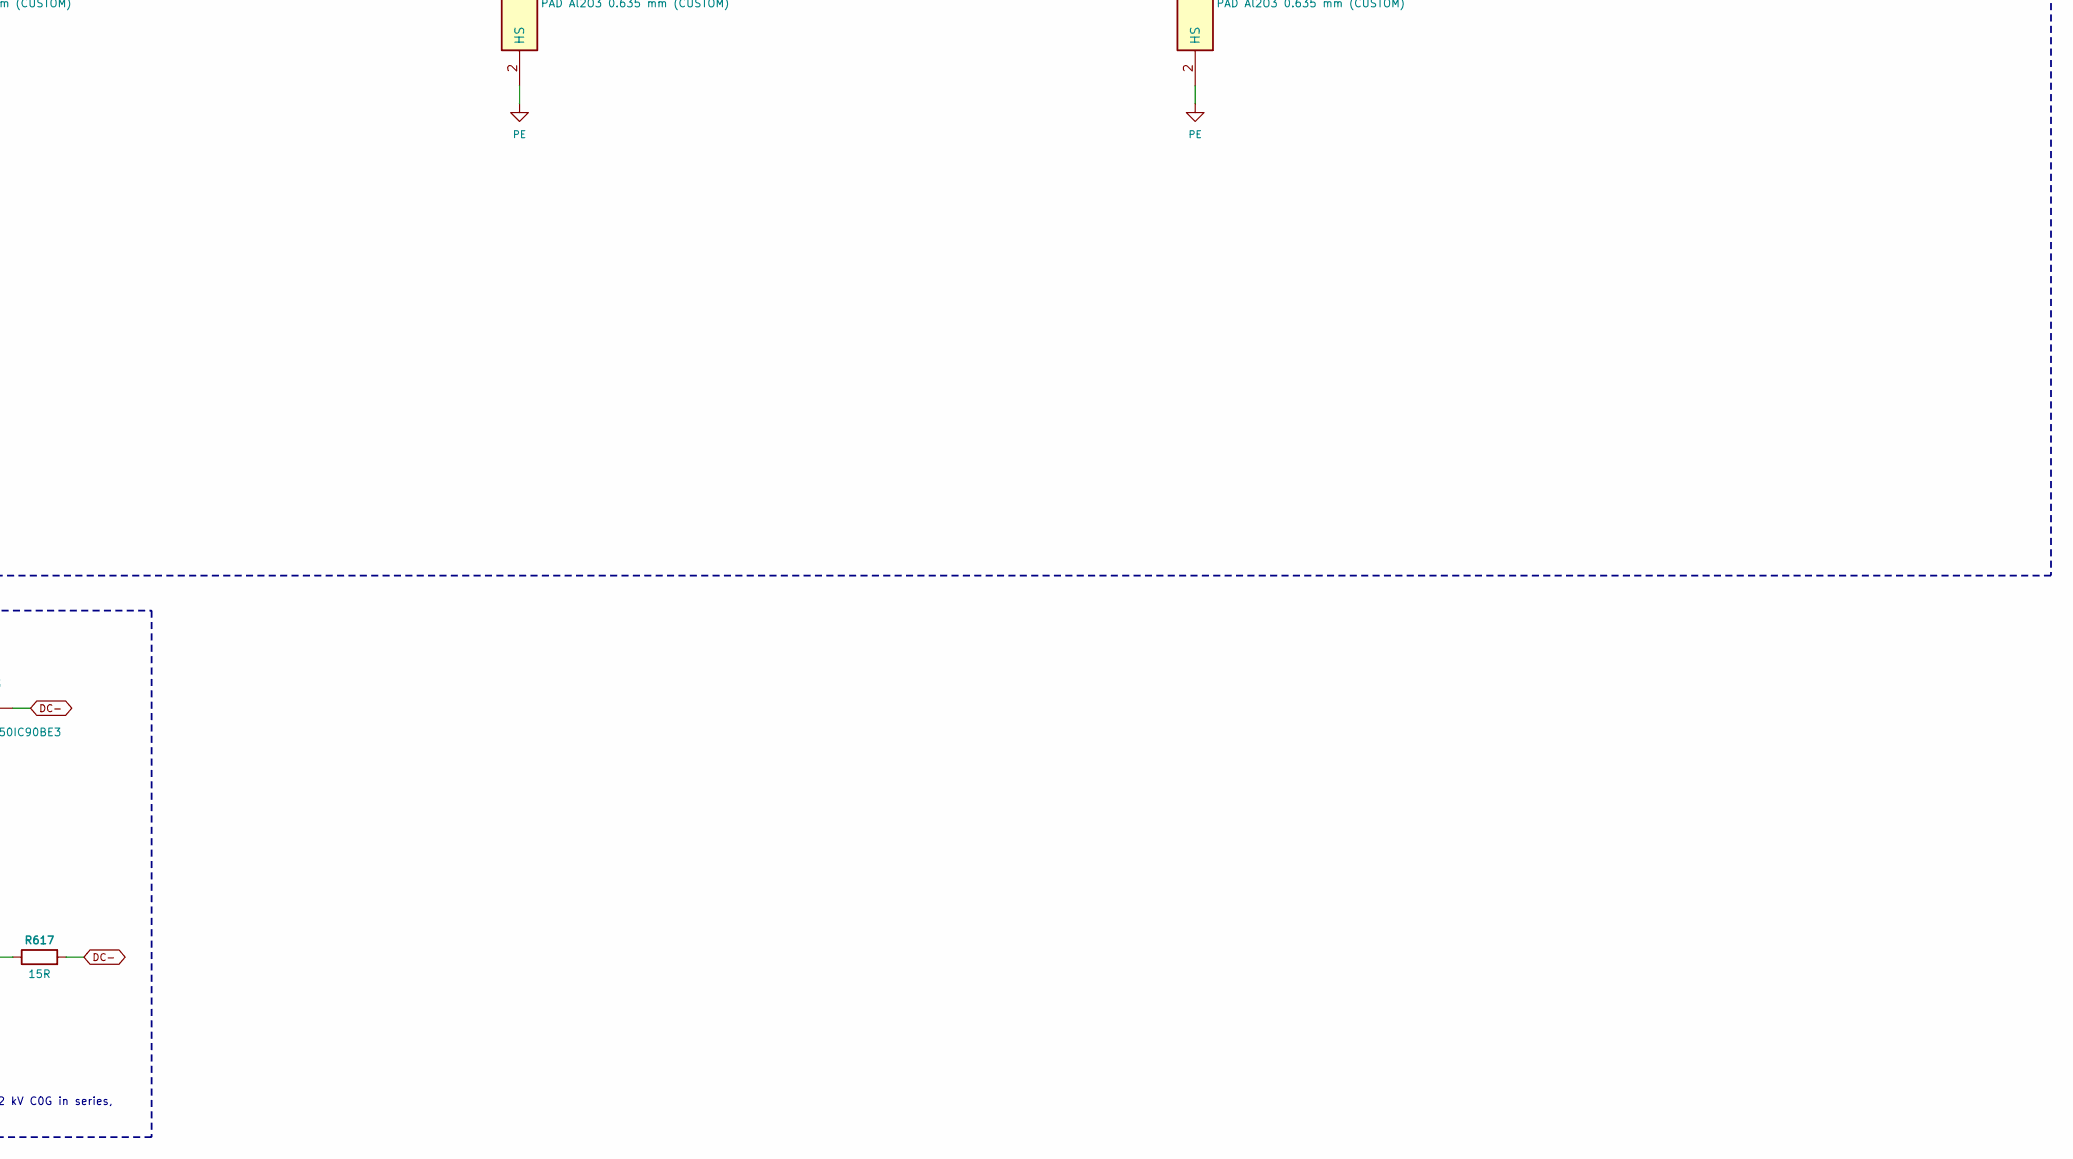
[picture p306: schematic 06_legn.kicad_sch, part in row 2, column 2]

Parts:
C601, C602, C603, C606, C607, C608, C611, C612, C613: FCSA3DS225K050IC90BE3; MPN FCSA3DS225K050IC90BE3
C604, C605, C609, C610, C614, C615: 4.7n 2000V
P601, P602, P603, P604, P605, P606, P607, P608, P609, P610, P611, P612: PAD Al2O3 0.635 mm (CUSTOM)
Q601, Q602, Q603, Q604, Q605, Q606, Q607, Q608, Q609, Q610, Q611, Q612: SG2M040170HJ; MPN SG2M040170HJ
R601, R602, R603, R604, R605, R606, R607, R608, R609, R610, R611, R612, R613, R614, R615, R616, R617, R618: 15R; MPN CRCW251215R0FKEGHP

Connections:
DC+: C601.1, C602.1, C603.1, C604.1, C606.1, C607.1, C608.1, C609.1, C611.1, C612.1, C613.1, C614.1, P601.1 (TAB), P602.1 (TAB), P603.1 (TAB), P604.1 (TAB), P605.1 (TAB), P606.1 (TAB), Q601.1 (D), Q601.5 (TAB), Q602.1 (D), Q602.5 (TAB), Q603.1 (D), Q603.5 (TAB), Q604.1 (D), Q604.5 (TAB), Q605.1 (D), Q605.5 (TAB), Q606.1 (D), Q606.5 (TAB)
DC-: C601.2, C602.2, C603.2, C606.2, C607.2, C608.2, C611.2, C612.2, C613.2, Q607.2 (S), Q608.2 (S), Q609.2 (S), Q610.2 (S), Q611.2 (S), Q612.2 (S), R604.2, R605.2, R606.2, R610.2, R611.2, R612.2, R616.2, R617.2, R618.2
DMP_N1_1: C604.2, C605.1
DMP_N1_2: C605.2, R601.1, R602.1, R603.1
DMP_N1_3: R601.2, R602.2, R603.2, R604.1, R605.1, R606.1
DMP_N2_1: C609.2, C610.1
DMP_N2_2: C610.2, R607.1, R608.1, R609.1
DMP_N2_3: R607.2, R608.2, R609.2, R610.1, R611.1, R612.1
DMP_N3_1: C614.2, C615.1
DMP_N3_2: C615.2, R613.1, R614.1, R615.1
DMP_N3_3: R613.2, R614.2, R615.2, R616.1, R617.1, R618.1
G_NH1: Q601.4 (G)
G_NH2: Q602.4 (G)
G_NH3: Q603.4 (G)
G_NH4: Q604.4 (G)
G_NH5: Q605.4 (G)
G_NH6: Q606.4 (G)
G_NL1: Q607.4 (G)
G_NL2: Q608.4 (G)
G_NL3: Q609.4 (G)
G_NL4: Q610.4 (G)
G_NL5: Q611.4 (G)
G_NL6: Q612.4 (G)
KS_NH1: Q601.3 (Driver_Source)
KS_NH2: Q602.3 (Driver_Source)
KS_NH3: Q603.3 (Driver_Source)
KS_NH4: Q604.3 (Driver_Source)
KS_NH5: Q605.3 (Driver_Source)
KS_NH6: Q606.3 (Driver_Source)
KS_NL1: Q607.3 (Driver_Source)
KS_NL2: Q608.3 (Driver_Source)
KS_NL3: Q609.3 (Driver_Source)
KS_NL4: Q610.3 (Driver_Source)
KS_NL5: Q611.3 (Driver_Source)
KS_NL6: Q612.3 (Driver_Source)
PE: P601.2 (HS), P602.2 (HS), P603.2 (HS), P604.2 (HS), P605.2 (HS), P606.2 (HS), P607.2 (HS), P608.2 (HS), P609.2 (HS), P610.2 (HS), P611.2 (HS), P612.2 (HS)
SW_N: P607.1 (TAB), P608.1 (TAB), P609.1 (TAB), P610.1 (TAB), P611.1 (TAB), P612.1 (TAB), Q601.2 (S), Q602.2 (S), Q603.2 (S), Q604.2 (S), Q605.2 (S), Q606.2 (S), Q607.1 (D), Q607.5 (TAB), Q608.1 (D), Q608.5 (TAB), Q609.1 (D), Q609.5 (TAB), Q610.1 (D), Q610.5 (TAB), Q611.1 (D), Q611.5 (TAB), Q612.1 (D), Q612.5 (TAB)

Notes on the sheet:
Per device: own gate net G_NH<k> and Kelvin net KS_NH<k> (gate network on the gate-drive sheet). BOM NOTE: R_DS(on) of the six within +/-5 % (V_GS 18 V, 38 A, 25 C), V_GS(th) within +/-0.25 V, one lot per switch (pcs_spec device_acceptance, PCM-06).
LEG N SUB-CELL 1: DECOUPLING + RC DAMPER
LEG N LOW SWITCH: 6 X SG2M040170HJ
3 x FCSA3DS225 at devices 1-2 (high and low); damper 2 x (3 x 15R) + 2 x 4.7n 2 kV C0G in series, loop at the pins <= 3 nH (LAYOUT).
Per device: own gate net G_NL<k> and Kelvin net KS_NL<k> (gate network on the gate-drive sheet). BOM NOTE: R_DS(on) of the six within +/-5 % (V_GS 18 V, 38 A, 25 C), V_GS(th) within +/-0.25 V, one lot per switch (pcs_spec device_acceptance, PCM-06).
3 x FCSA3DS225 at devices 3-4 (high and low); damper 2 x (3 x 15R) + 2 x 4.7n 2 kV C0G in series, loop at the pins <= 3 nH (LAYOUT).
LEG N SUB-CELL 2: DECOUPLING + RC DAMPER
LEG N SUB-CELL 3: DECOUPLING + RC DAMPER
LEG N HIGH SWITCH: 6 X SG2M040170HJ
3 x FCSA3DS225 at devices 5-6 (high and low); damper 2 x (3 x 15R) + 2 x 4.7n 2 kV C0G in series, loop at the pins <= 3 nH (LAYOUT).
