vectivolt/PCM/hardware/PCS-PWR-4W/sheets/07_gdah.kicad_sch

## KiCad design hardware/PCS-PWR-4W/sheets/07_gdah.kicad_sch (2026-10-07)

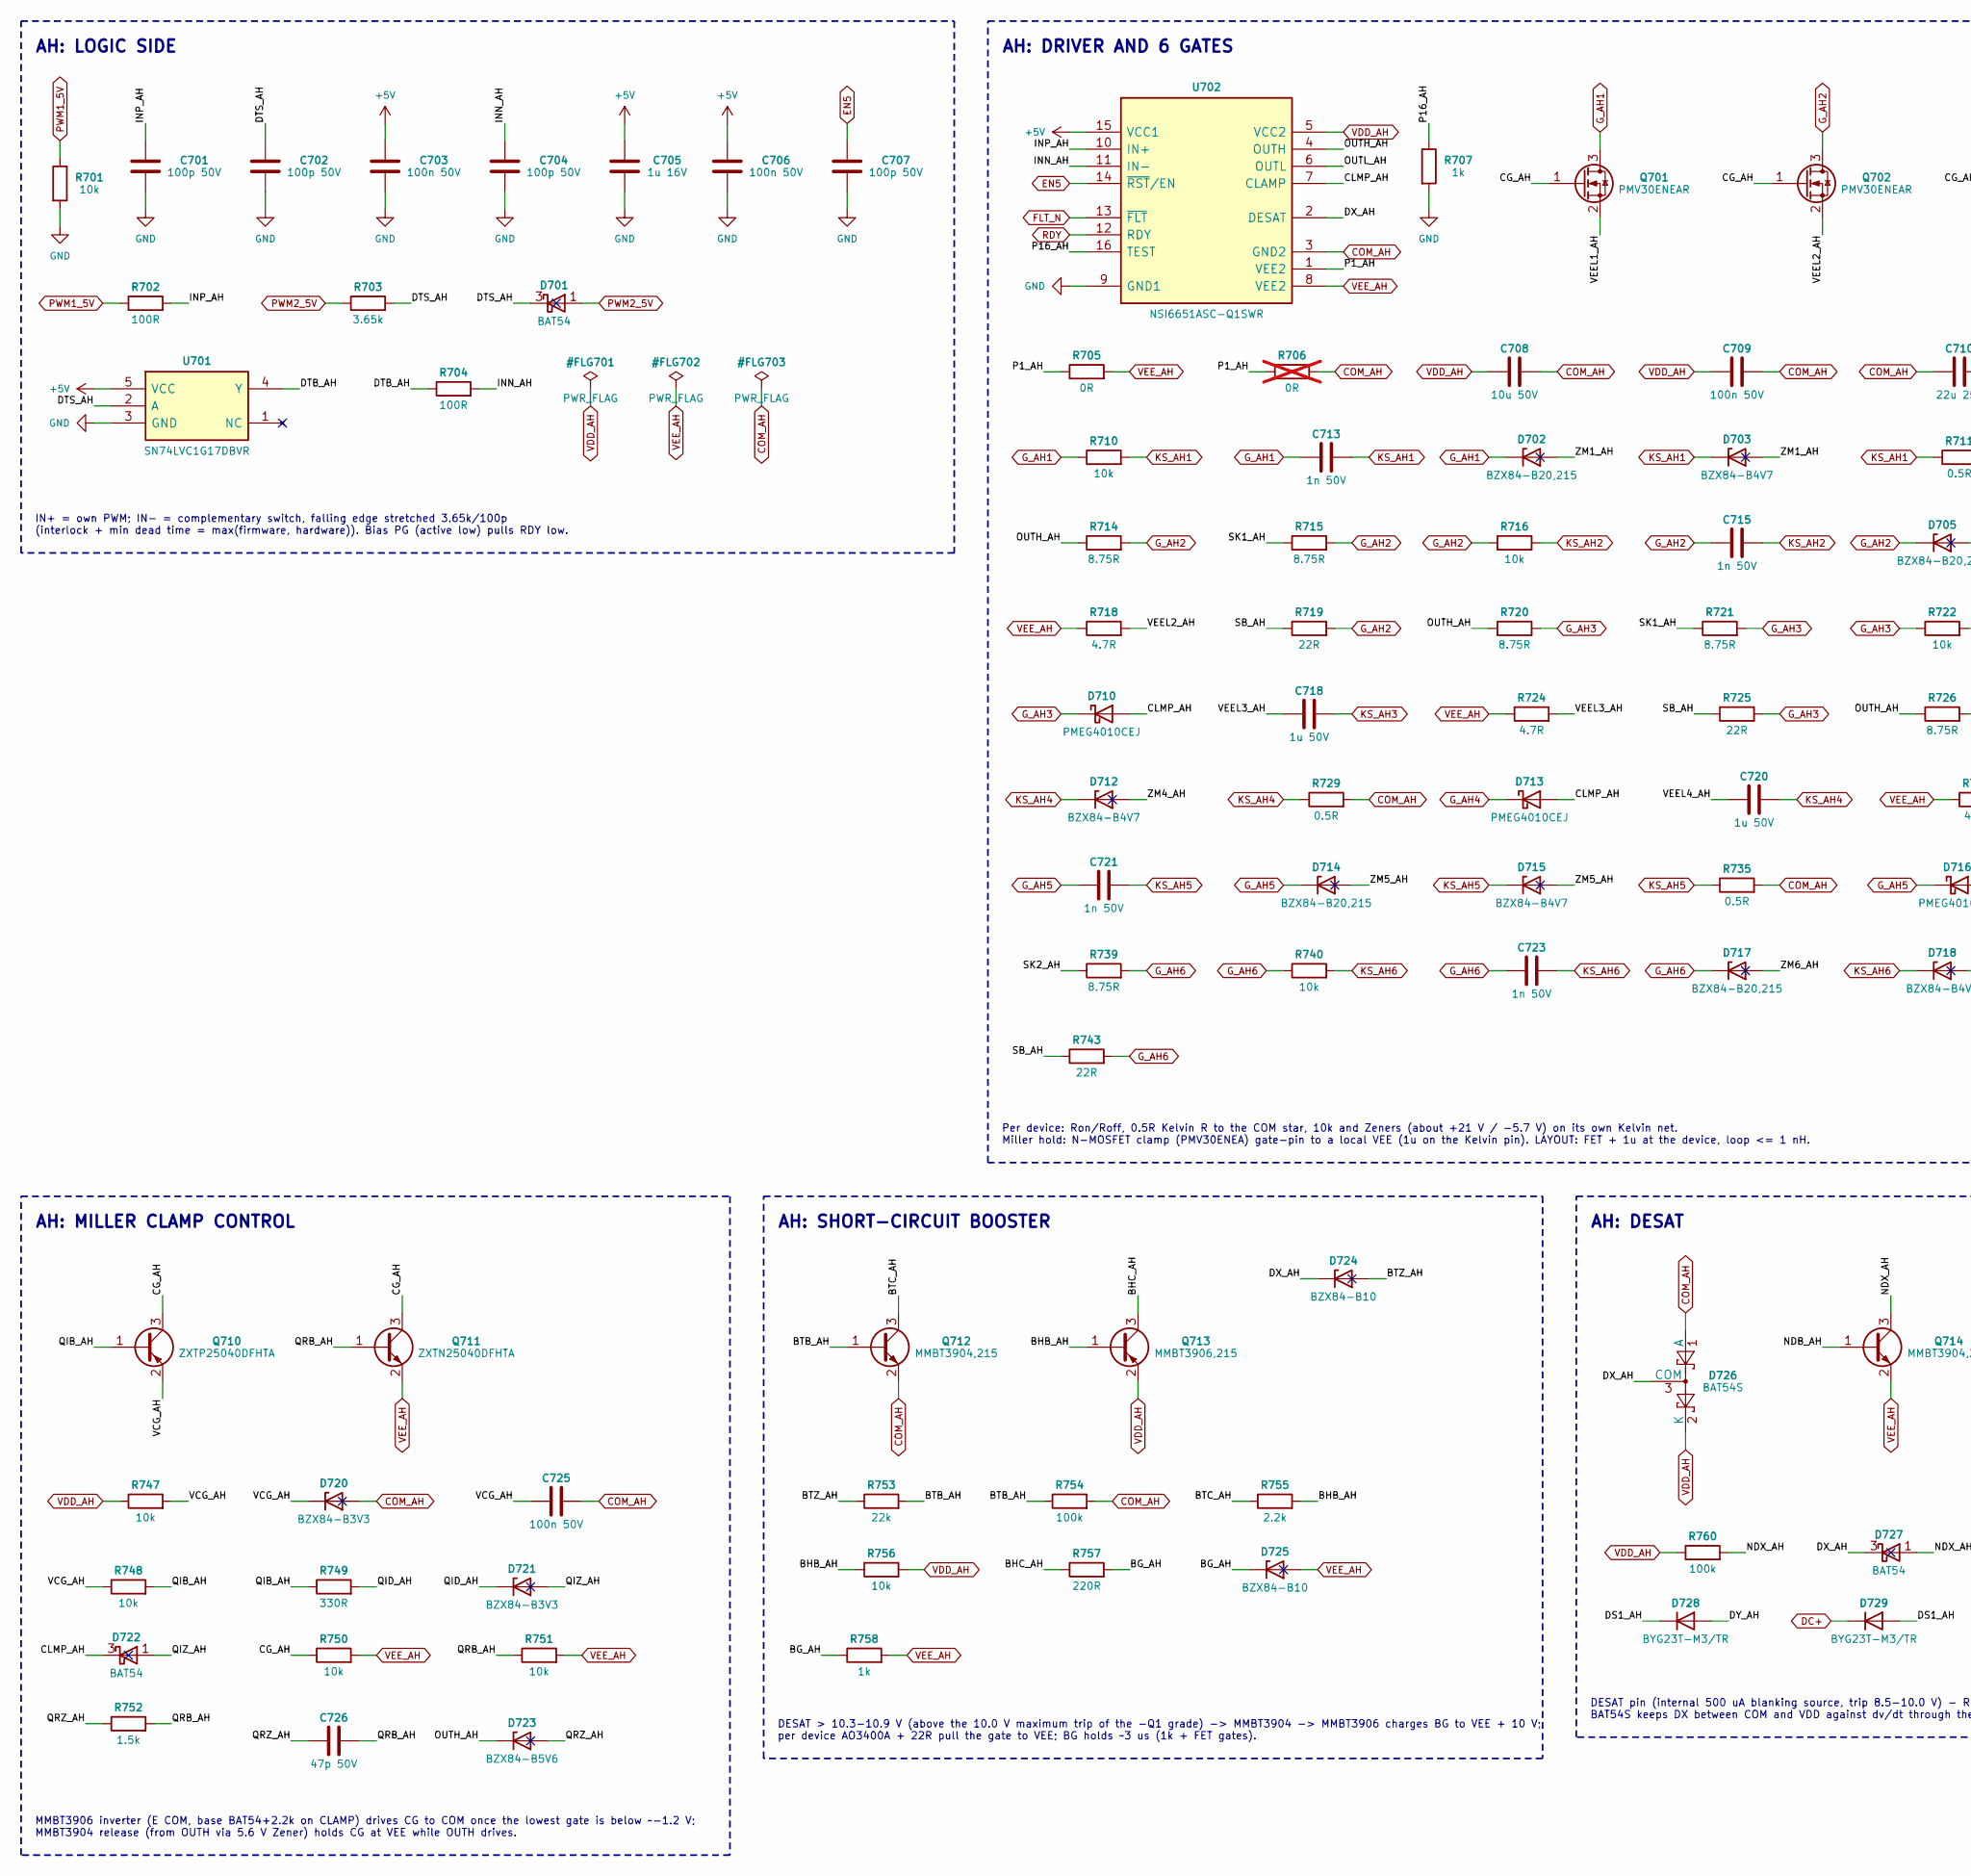
[picture p307: schematic 07_gdah.kicad_sch, part in row 1, column 1]

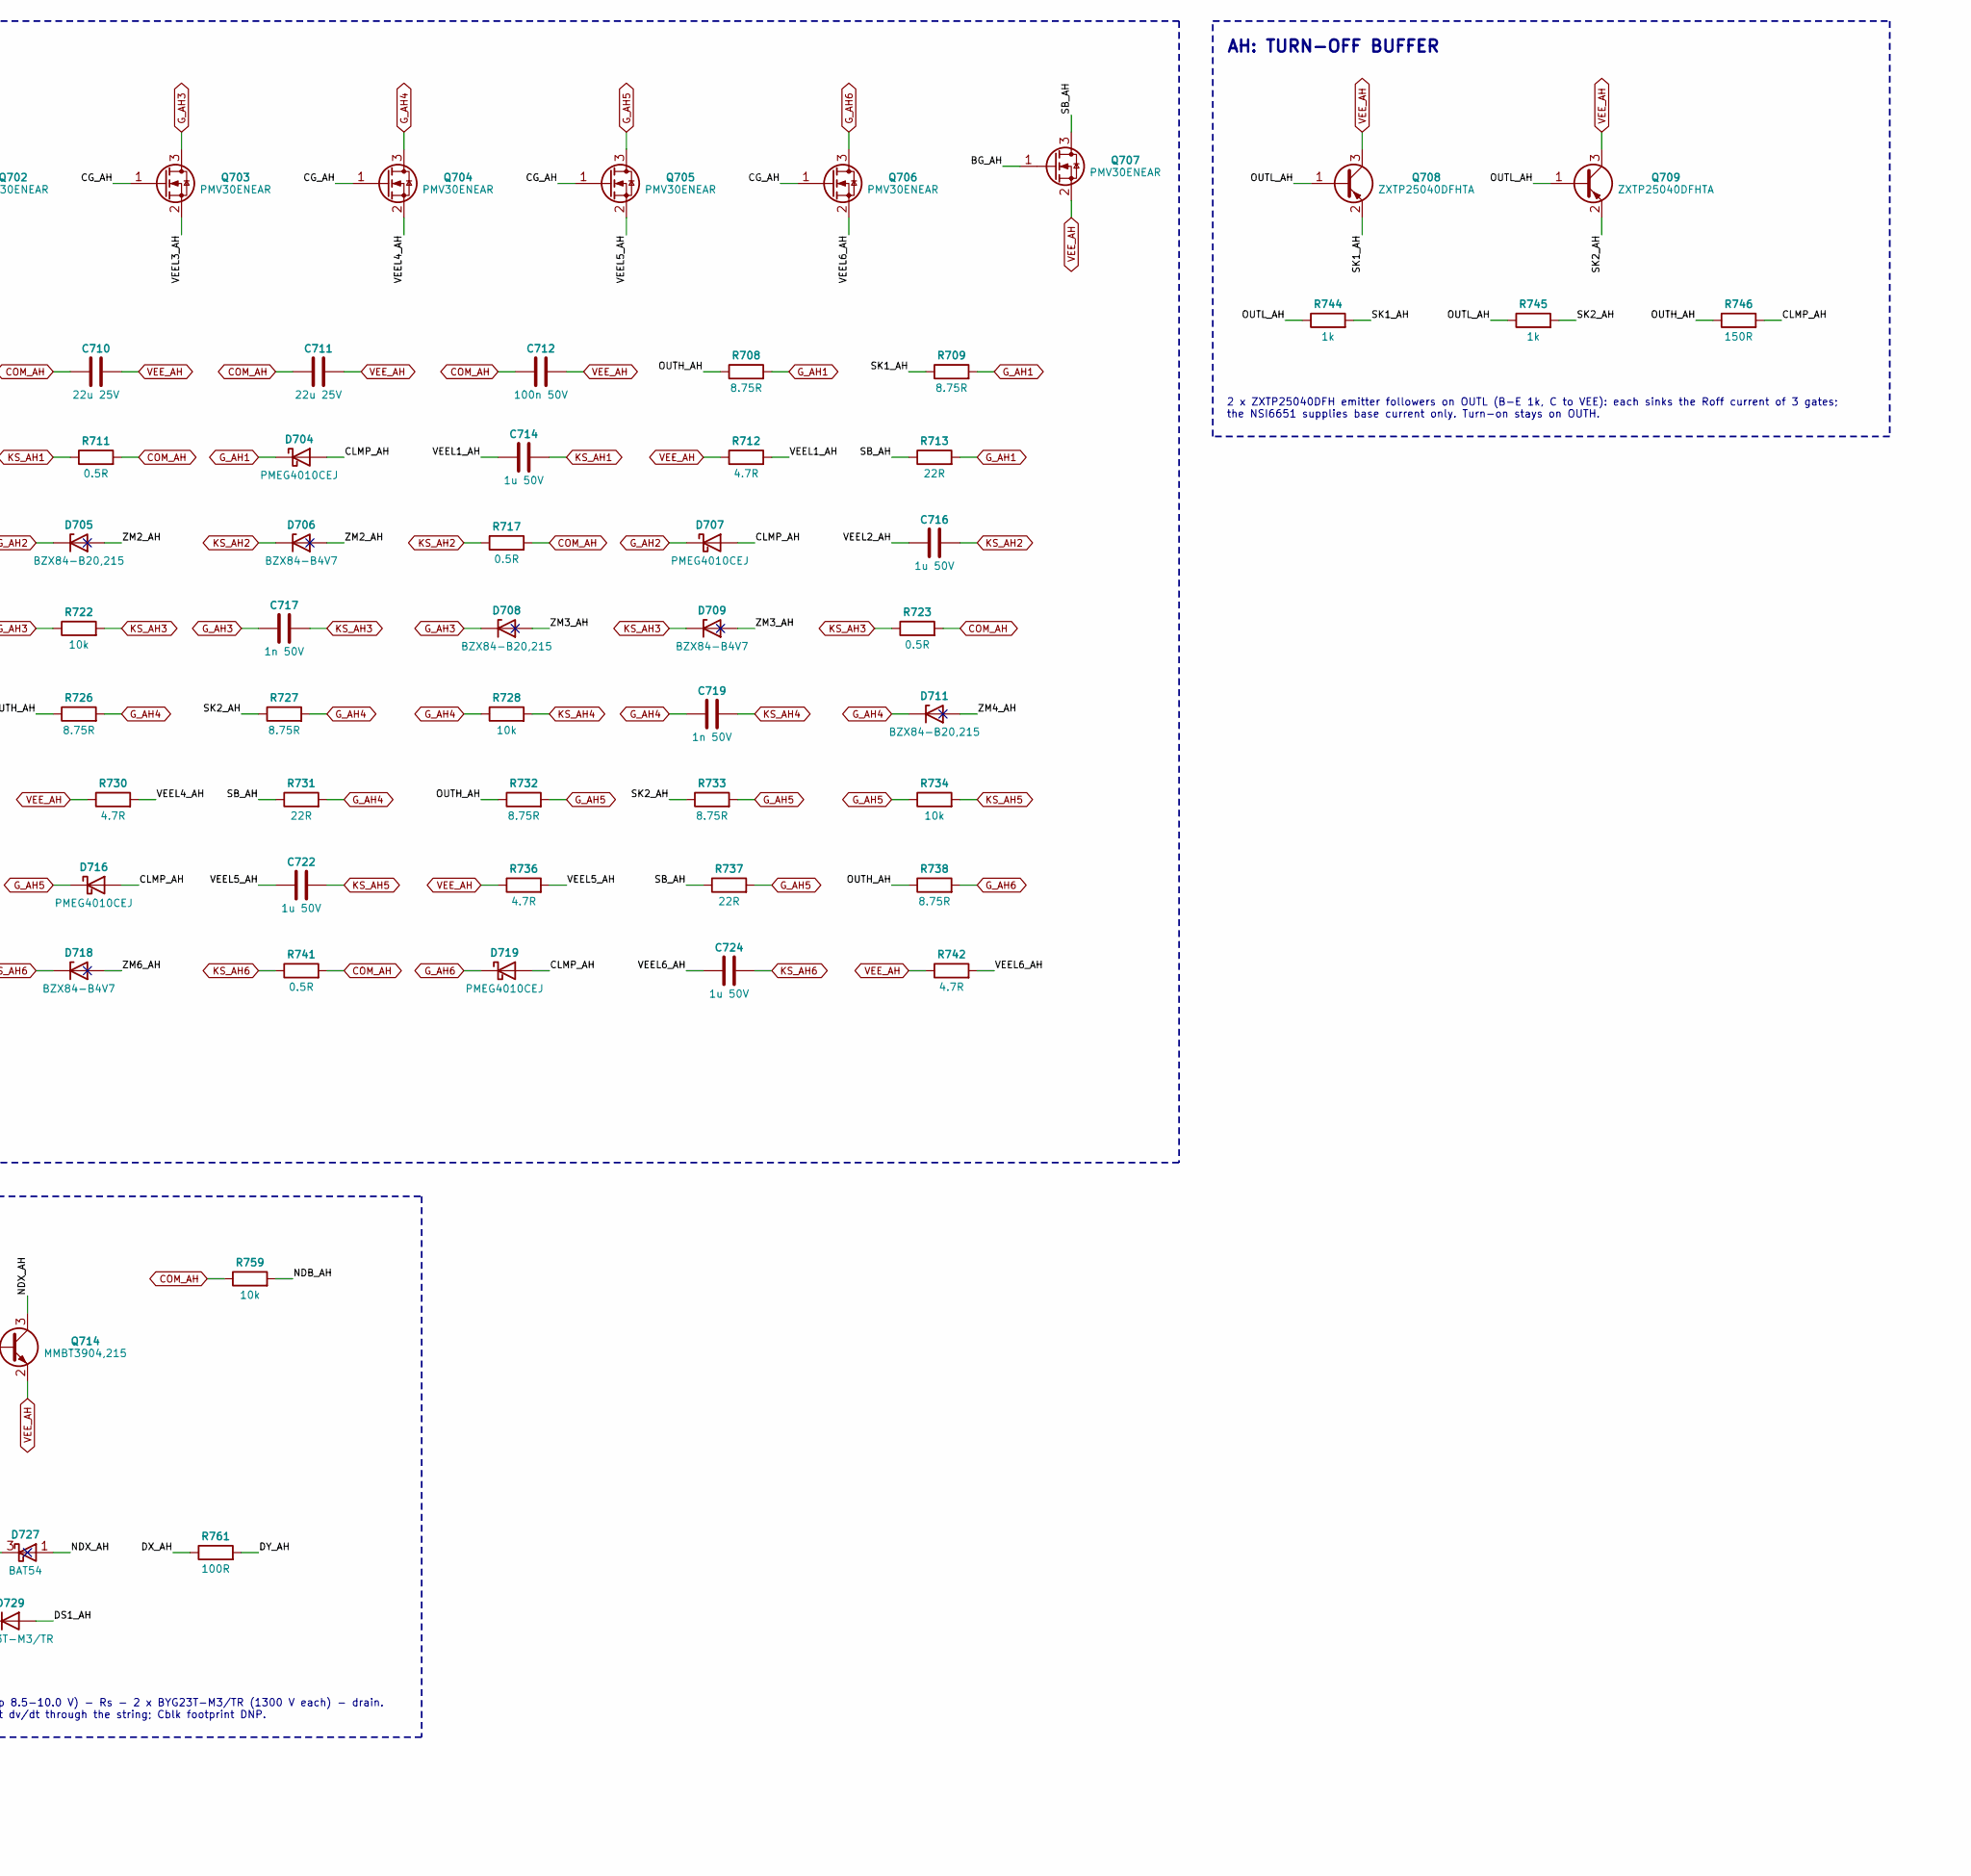
[picture p308: schematic 07_gdah.kicad_sch, part in row 1, column 2]

Parts:
C701, C702, C704, C707: 100p 50V
C703, C706, C709, C712, C725: 100n 50V
C705: 1u 16V
C708: 10u 50V
C710, C711: 22u 25V
C713, C715, C717, C719, C721, C723: 1n 50V
C714, C716, C718, C720, C722, C724: 1u 50V
C726: 47p 50V
D701, D722, D727: BAT54; MPN BAT54
D702, D705, D708, D711, D714, D717: BZX84-B20,215; MPN BZX84-B20,215
D703, D706, D709, D712, D715, D718: BZX84-B4V7; MPN BZX84-B4V7
D704, D707, D710, D713, D716, D719: PMEG4010CEJ; MPN PMEG4010CEJ
D720, D721: BZX84-B3V3; MPN BZX84-B3V3
D723: BZX84-B5V6; MPN BZX84-B5V6
D724, D725: BZX84-B10; MPN BZX84-B10
D726: BAT54S; MPN BAT54S
D728, D729: BYG23T-M3/TR; MPN BYG23T-M3/TR
Q701, Q702, Q703, Q704, Q705, Q706, Q707: PMV30ENEAR; MPN PMV30ENEAR
Q708, Q709, Q710: ZXTP25040DFHTA; MPN ZXTP25040DFHTA
Q711: ZXTN25040DFHTA; MPN ZXTN25040DFHTA
Q712, Q714: MMBT3904,215; MPN MMBT3904,215
Q713: MMBT3906,215; MPN MMBT3906,215
R701, R710, R716, R722, R728, R734, R740, R747, R748, R750, R751, R756, R759: 10k
R702, R704, R761: 100R
R703: 3.65k
R705: 0R
R706: 0R; not fitted
R707, R744, R745, R758: 1k
R708, R709, R714, R715, R720, R721, R726, R727, R732, R733, R738, R739: 8.75R
R711, R717, R723, R729, R735, R741: 0.5R
R712, R718, R724, R730, R736, R742: 4.7R
R713, R719, R725, R731, R737, R743: 22R
R746: 150R
R749: 330R
R752: 1.5k
R753: 22k
R754, R760: 100k
R755: 2.2k
R757: 220R
U701: SN74LVC1G17DBVR; MPN SN74LVC1G17DBVR
U702: NSI6651ASC-Q1SWR; MPN NSI6651ASC-Q1SWR

Connections:
+5V: C703.1, C705.1, C706.1, U701.5 (VCC), U702.15 (VCC1)
BG_AH: D725.3 (K), Q707.1 (G), R757.2, R758.1
BHB_AH: Q713.1 (B), R755.2, R756.1
BHC_AH: Q713.3 (C), R757.1
BTB_AH: Q712.1 (B), R753.2, R754.1
BTC_AH: Q712.3 (C), R755.1
BTZ_AH: D724.1 (A), R753.1
CG_AH: Q701.1 (G), Q702.1 (G), Q703.1 (G), Q704.1 (G), Q705.1 (G), Q706.1 (G), Q710.3 (C), Q711.3 (C), R750.1
CLMP_AH: D704.2 (A), D707.2 (A), D710.2 (A), D713.2 (A), D716.2 (A), D719.2 (A), D722.3 (K), R746.2, U702.7 (CLAMP)
COM_AH: C708.2, C709.2, C710.1, C711.1, C712.1, C725.2, D720.1 (A), D726.1 (A), Q712.2 (E), R706.2, R711.2, R717.2, R723.2, R729.2, R735.2, R741.2, R754.2, R759.1, U702.3 (GND2)
DC+: D729.1 (K)
DS1_AH: D728.1 (K), D729.2 (A)
DTB_AH: R704.1, U701.4 (Y)
DTS_AH: C702.1, D701.3 (K), R703.2, U701.2 (A)
DX_AH: D724.3 (K), D726.3 (COM), D727.3 (K), R761.1, U702.2 (DESAT)
DY_AH: D728.2 (A), R761.2
EN5: C707.1, U702.14 (~RST/EN)
FLT_N: U702.13 (~FLT)
GND: C701.2, C702.2, C703.2, C704.2, C705.2, C706.2, C707.2, R701.2, R707.2, U701.3 (GND), U702.9 (GND1)
G_AH1: C713.1, D702.3 (K), D704.1 (K), Q701.3 (D), R708.2, R709.2, R710.1, R713.2
G_AH2: C715.1, D705.3 (K), D707.1 (K), Q702.3 (D), R714.2, R715.2, R716.1, R719.2
G_AH3: C717.1, D708.3 (K), D710.1 (K), Q703.3 (D), R720.2, R721.2, R722.1, R725.2
G_AH4: C719.1, D711.3 (K), D713.1 (K), Q704.3 (D), R726.2, R727.2, R728.1, R731.2
G_AH5: C721.1, D714.3 (K), D716.1 (K), Q705.3 (D), R732.2, R733.2, R734.1, R737.2
G_AH6: C723.1, D717.3 (K), D719.1 (K), Q706.3 (D), R738.2, R739.2, R740.1, R743.2
INN_AH: C704.1, R704.2, U702.11 (IN-)
INP_AH: C701.1, R702.2, U702.10 (IN+)
KS_AH1: C713.2, C714.2, D703.3 (K), R710.2, R711.1
KS_AH2: C715.2, C716.2, D706.3 (K), R716.2, R717.1
KS_AH3: C717.2, C718.2, D709.3 (K), R722.2, R723.1
KS_AH4: C719.2, C720.2, D712.3 (K), R728.2, R729.1
KS_AH5: C721.2, C722.2, D715.3 (K), R734.2, R735.1
KS_AH6: C723.2, C724.2, D718.3 (K), R740.2, R741.1
NDB_AH: Q714.1 (B), R759.2
NDX_AH: D727.1 (A), Q714.3 (C), R760.2
OUTH_AH: D723.3 (K), R708.1, R714.1, R720.1, R726.1, R732.1, R738.1, R746.1, U702.4 (OUTH)
OUTL_AH: Q708.1 (B), Q709.1 (B), R744.1, R745.1, U702.6 (OUTL)
P1_AH: R705.1, R706.1, U702.1 (VEE2)
P16_AH: R707.1, U702.16 (TEST)
PWM1_5V: R701.1, R702.1
PWM2_5V: D701.1 (A), R703.1
QIB_AH: Q710.1 (B), R748.2, R749.1
QID_AH: D721.3 (K), R749.2
QIZ_AH: D721.1 (A), D722.1 (A)
QRB_AH: C726.2, Q711.1 (B), R751.1, R752.2
QRZ_AH: C726.1, D723.1 (A), R752.1
RDY: U702.12 (RDY)
SB_AH: Q707.3 (D), R713.1, R719.1, R725.1, R731.1, R737.1, R743.1
SK1_AH: Q708.2 (E), R709.1, R715.1, R721.1, R744.2
SK2_AH: Q709.2 (E), R727.1, R733.1, R739.1, R745.2
VCG_AH: C725.1, D720.3 (K), Q710.2 (E), R747.2, R748.1
VDD_AH: C708.1, C709.1, D726.2 (K), Q713.2 (E), R747.1, R756.2, R760.1, U702.5 (VCC2)
VEEL1_AH: C714.1, Q701.2 (S), R712.2
VEEL2_AH: C716.1, Q702.2 (S), R718.2
VEEL3_AH: C718.1, Q703.2 (S), R724.2
VEEL4_AH: C720.1, Q704.2 (S), R730.2
VEEL5_AH: C722.1, Q705.2 (S), R736.2
VEEL6_AH: C724.1, Q706.2 (S), R742.2
VEE_AH: C710.2, C711.2, C712.2, D725.1 (A), Q707.2 (S), Q708.3 (C), Q709.3 (C), Q711.2 (E), Q714.2 (E), R705.2, R712.1, R718.1, R724.1, R730.1, R736.1, R742.1, R750.2, R751.2, R758.2, U702.8 (VEE2)
ZM1_AH: D702.1 (A), D703.1 (A)
ZM2_AH: D705.1 (A), D706.1 (A)
ZM3_AH: D708.1 (A), D709.1 (A)
ZM4_AH: D711.1 (A), D712.1 (A)
ZM5_AH: D714.1 (A), D715.1 (A)
ZM6_AH: D717.1 (A), D718.1 (A)

Notes on the sheet:
DESAT > 10.3-10.9 V (above the 10.0 V maximum trip of the -Q1 grade) -> MMBT3904 -> MMBT3906 charges BG to VEE + 10 V; per device AO3400A + 22R pull the gate to VEE; BG holds ~3 us (1k + FET gates).
AH: MILLER CLAMP CONTROL
IN+ = own PWM; IN- = complementary switch, falling edge stretched 3.65k/100p (interlock + min dead time = max(firmware, hardware)). Bias PG (active low) pulls RDY low.
AH: SHORT-CIRCUIT BOOSTER
2 x ZXTP25040DFH emitter followers on OUTL (B-E 1k, C to VEE): each sinks the Roff current of 3 gates; the NSI6651 supplies base current only. Turn-on stays on OUTH.
MMBT3906 inverter (E COM, base BAT54+2.2k on CLAMP) drives CG to COM once the lowest gate is below ~-1.2 V; MMBT3904 release (from OUTH via 5.6 V Zener) holds CG at VEE while OUTH drives.
Per device: Ron/Roff, 0.5R Kelvin R to the COM star, 10k and Zeners (about +21 V / -5.7 V) on its own Kelvin net. Miller hold: N-MOSFET clamp (PMV30ENEA) gate-pin to a local VEE (1u on the Kelvin pin). LAYOUT: FET + 1u at the device, loop <= 1 nH.
AH: TURN-OFF BUFFER
DESAT pin (internal 500 uA blanking source, trip 8.5-10.0 V) - Rs - 2 x BYG23T-M3/TR (1300 V each) - drain. BAT54S keeps DX between COM and VDD against dv/dt through the string; Cblk footprint DNP.
AH: LOGIC SIDE
AH: DRIVER AND 6 GATES
AH: DESAT
