vectivolt/PCM/hardware/PCS-PWR-4W/sheets/08_gdal.kicad_sch

## KiCad design hardware/PCS-PWR-4W/sheets/08_gdal.kicad_sch (2026-10-07)

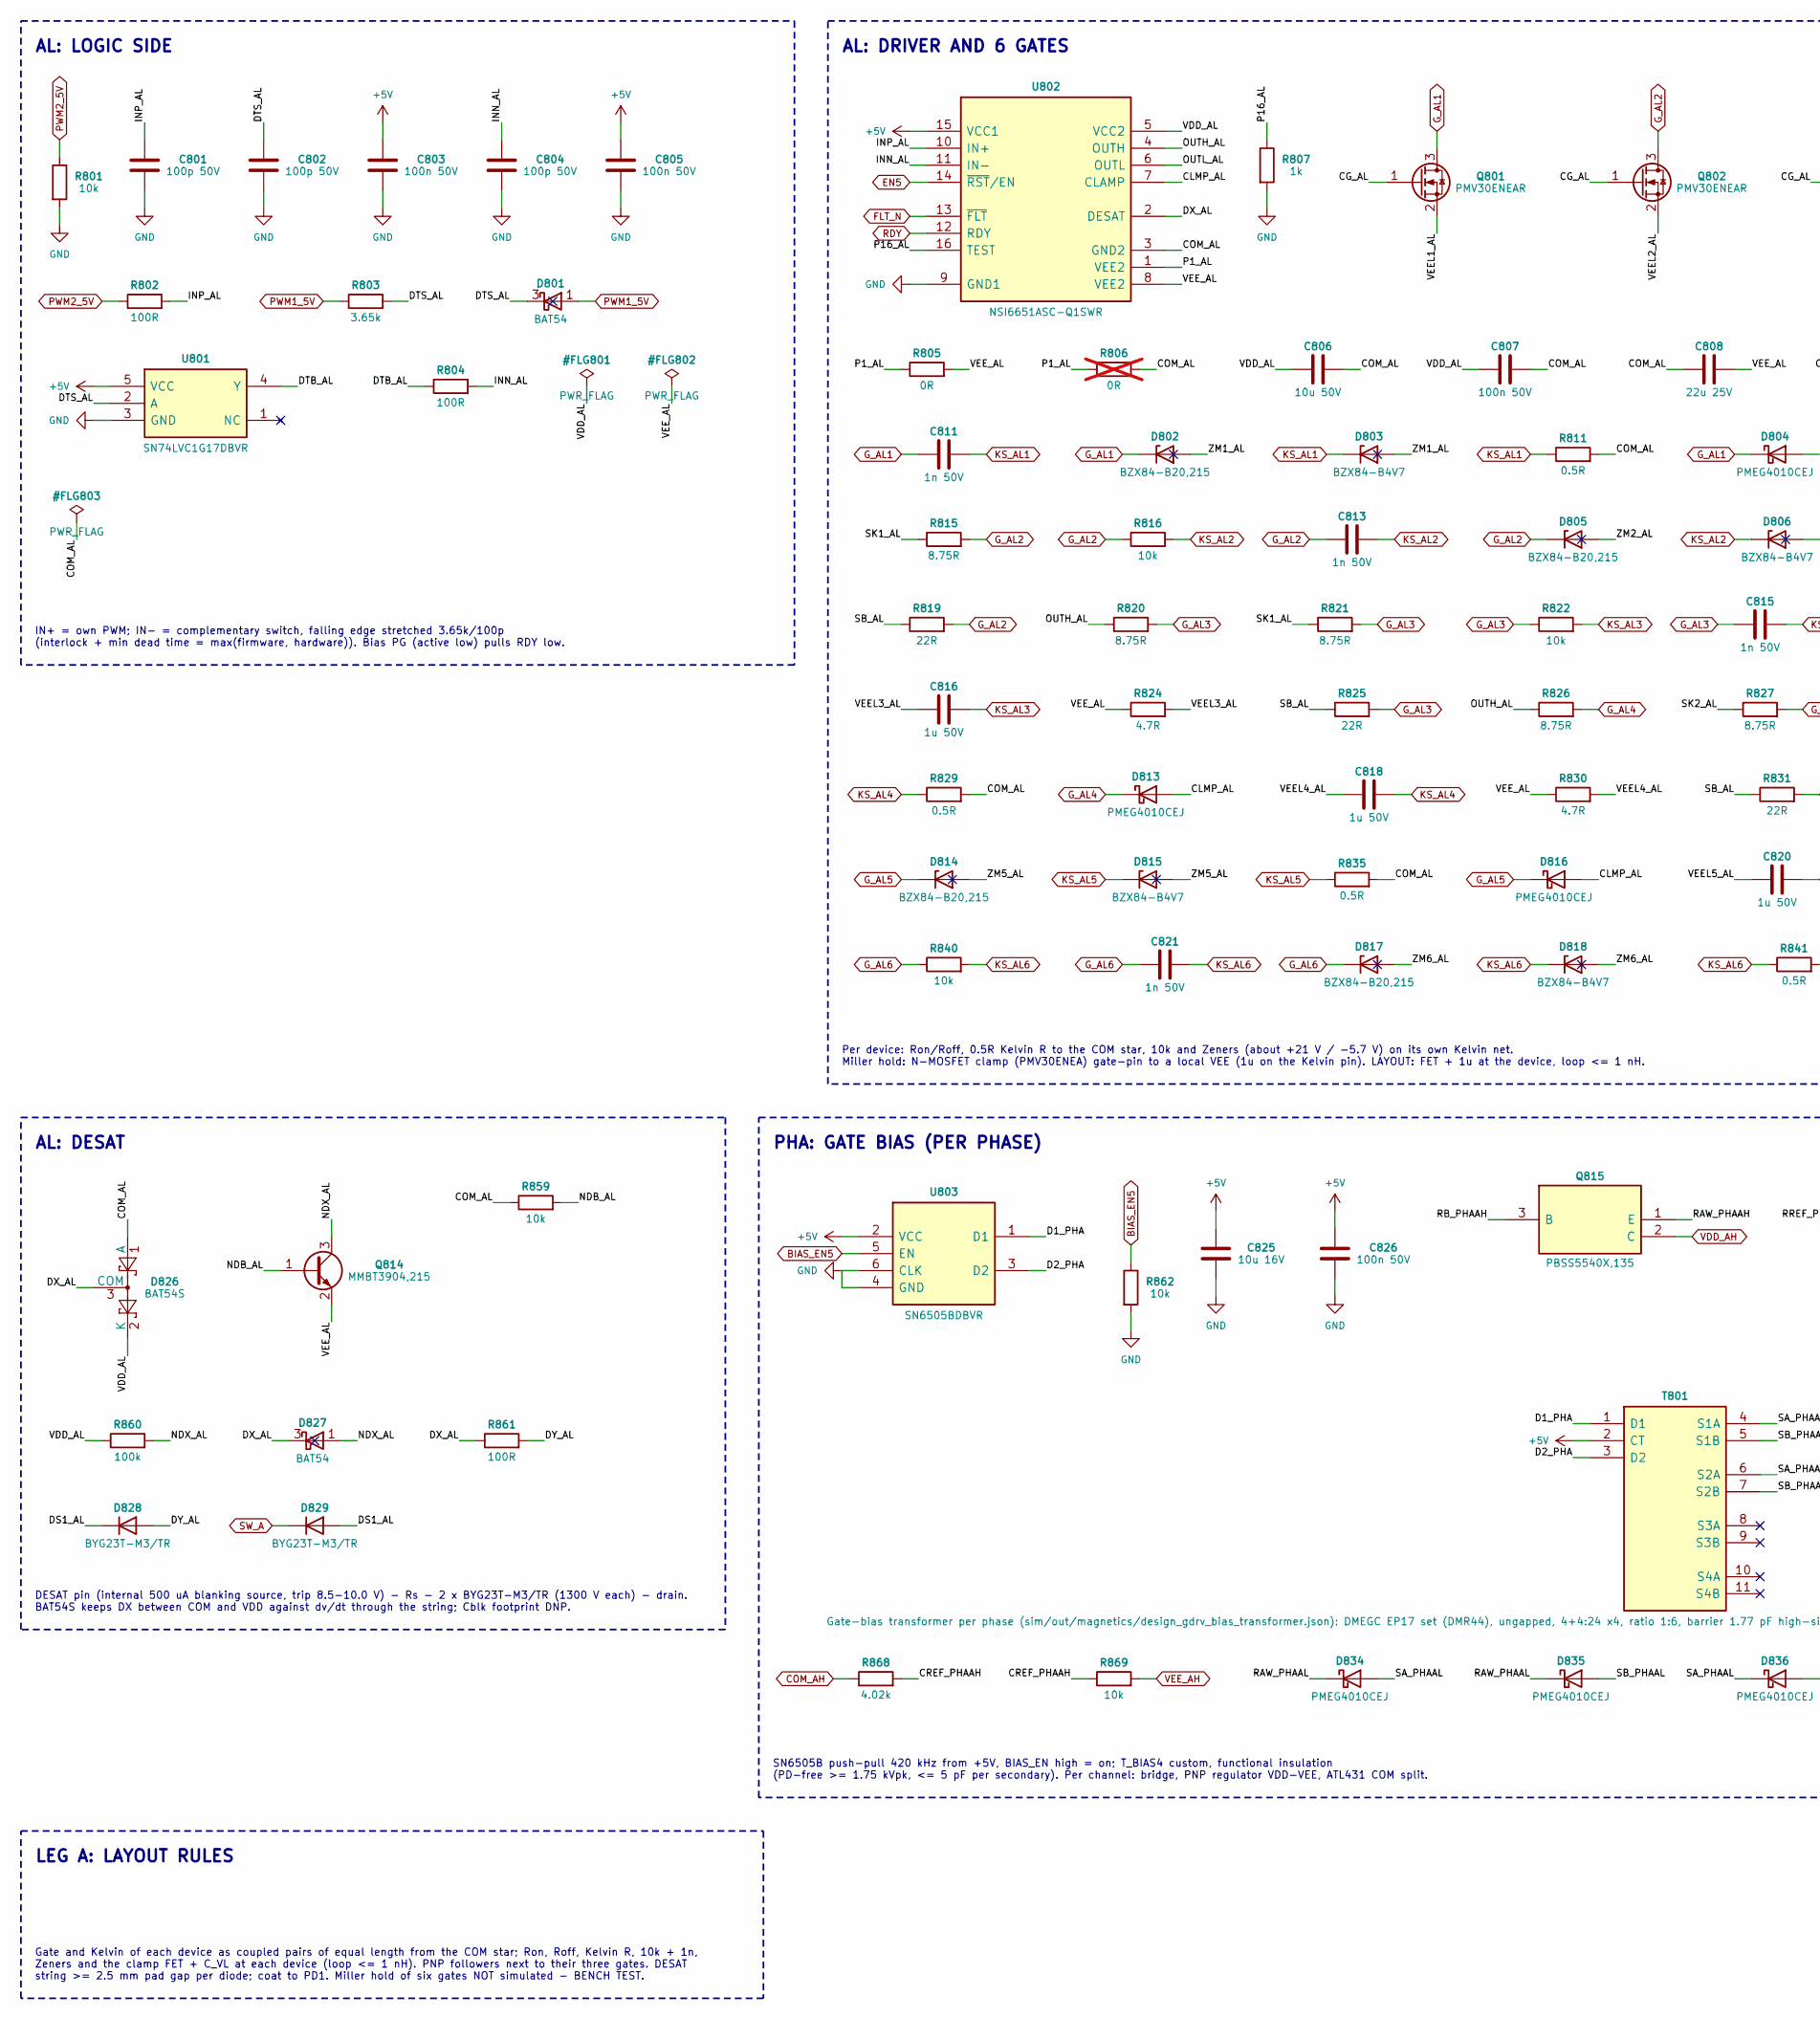
[picture p309: schematic 08_gdal.kicad_sch, part in row 1, column 1]

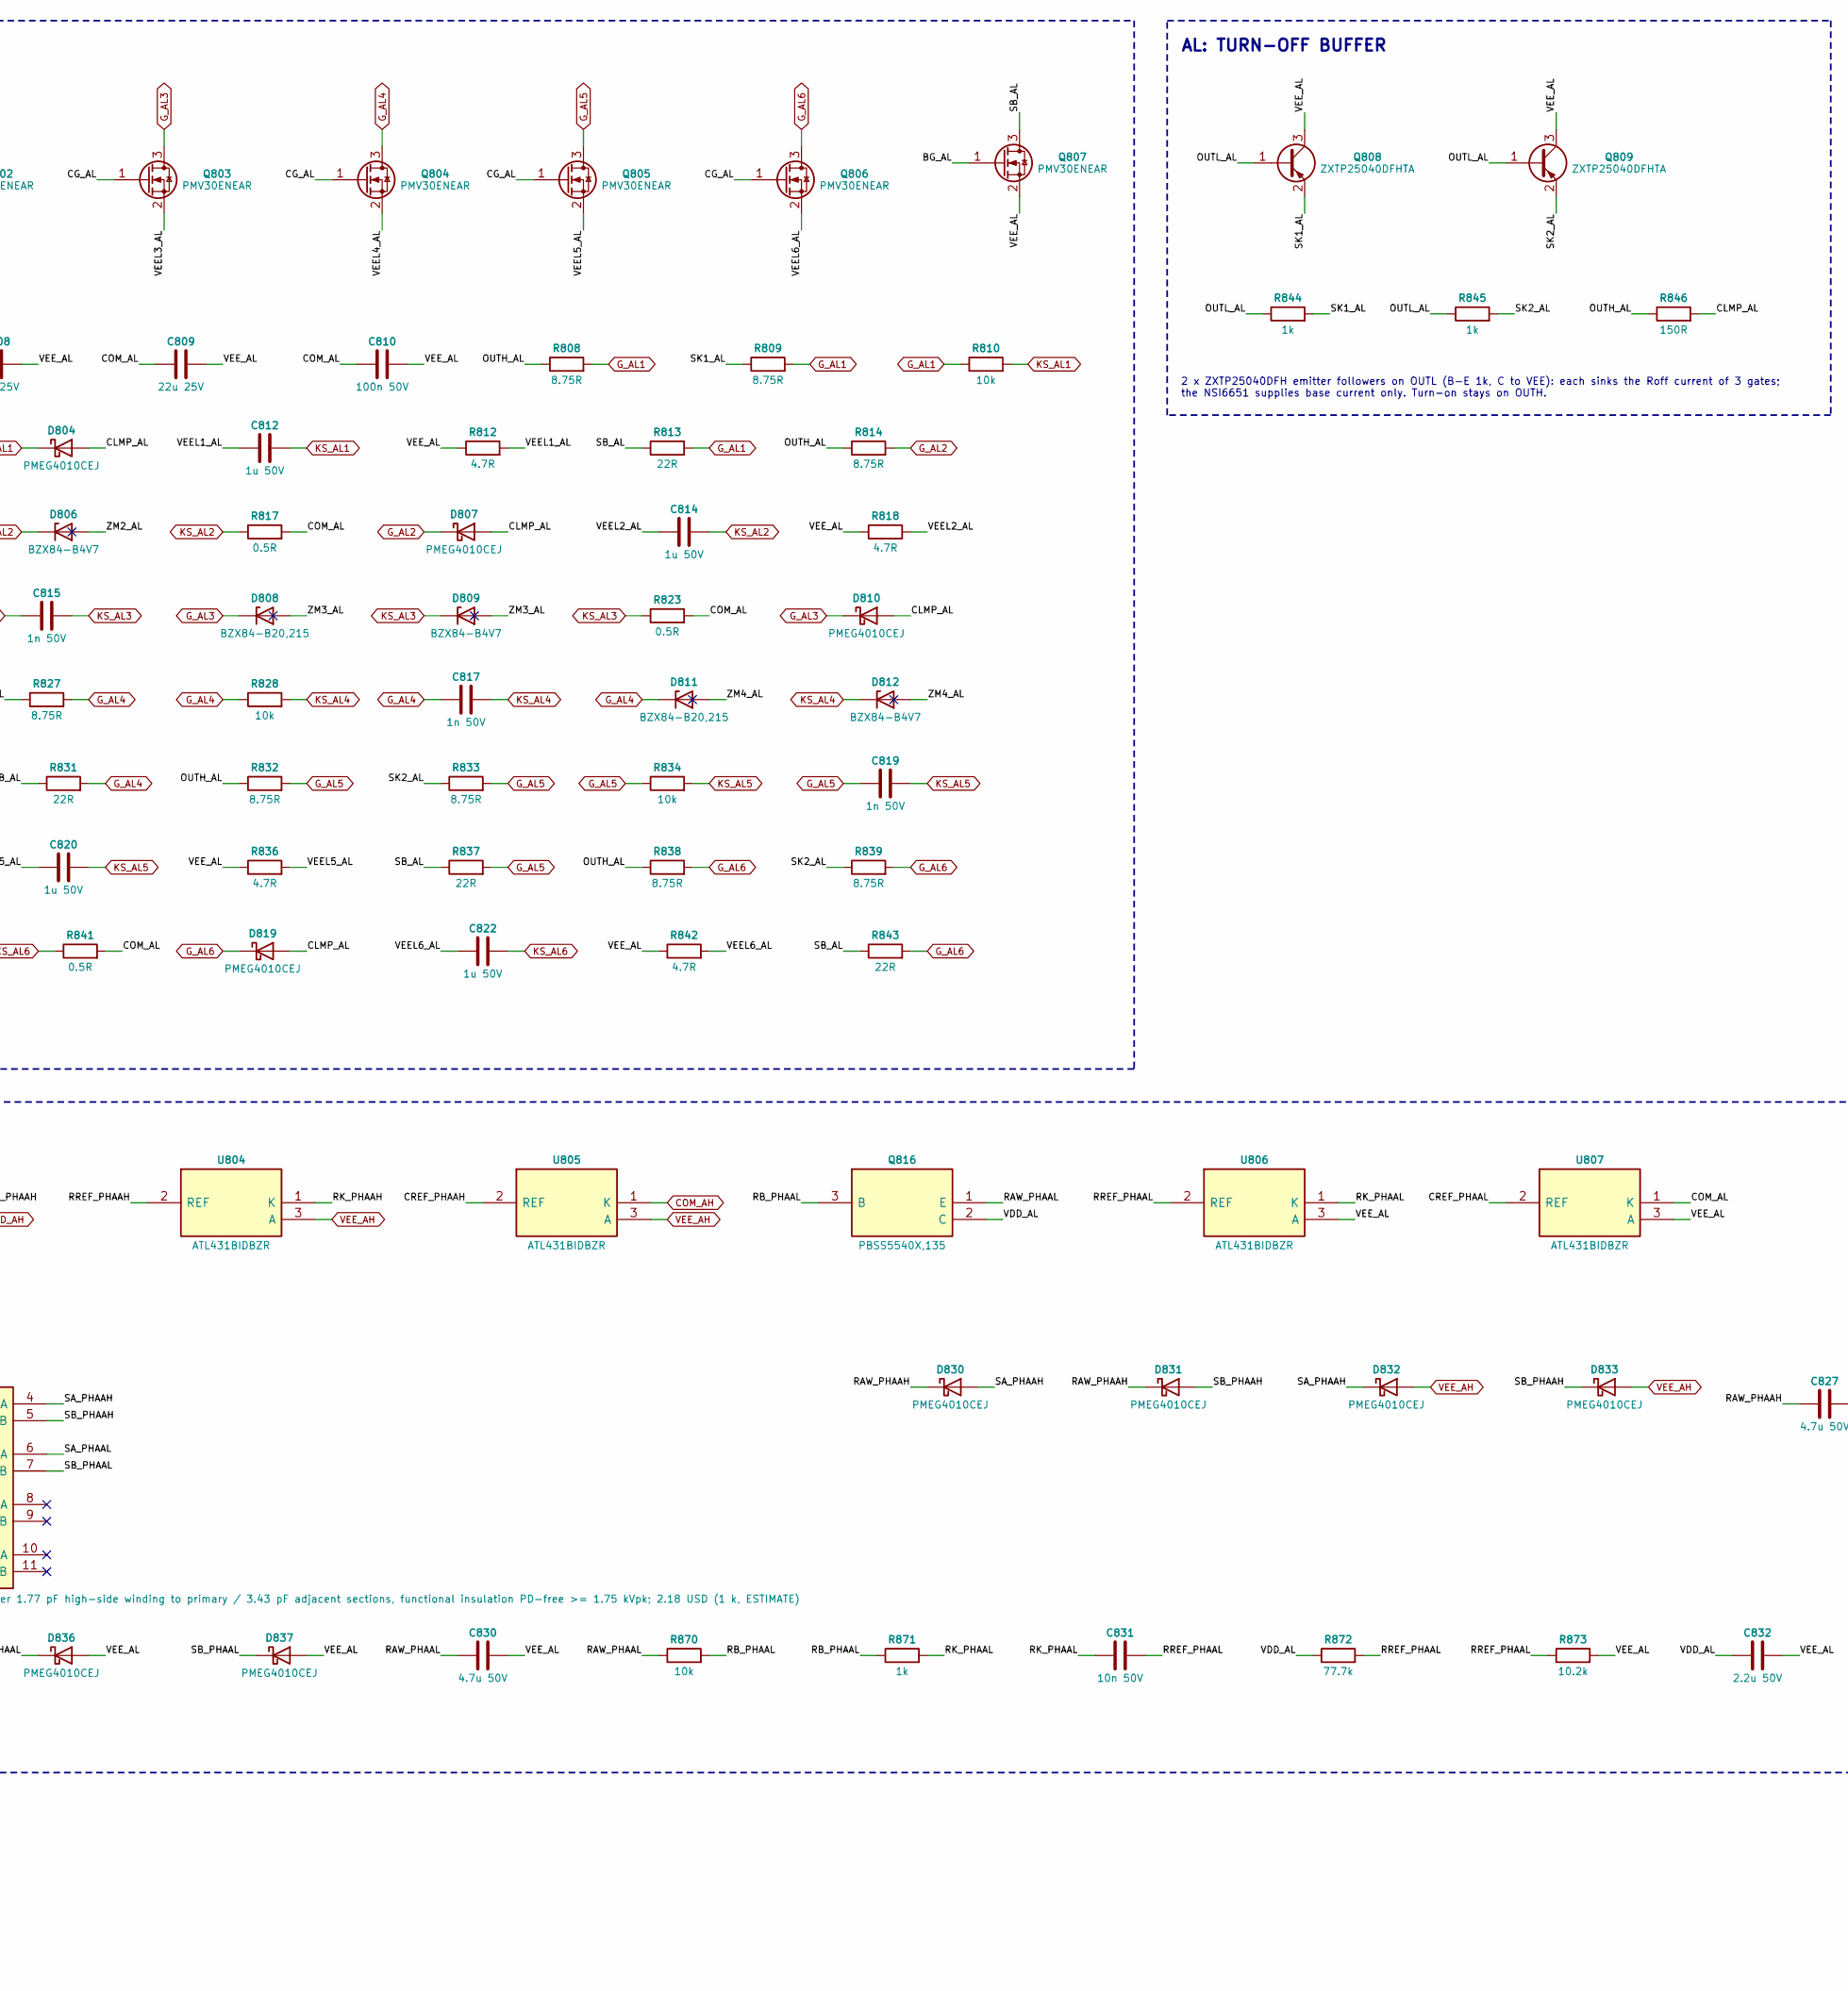
[picture p310: schematic 08_gdal.kicad_sch, part in row 1, column 2]

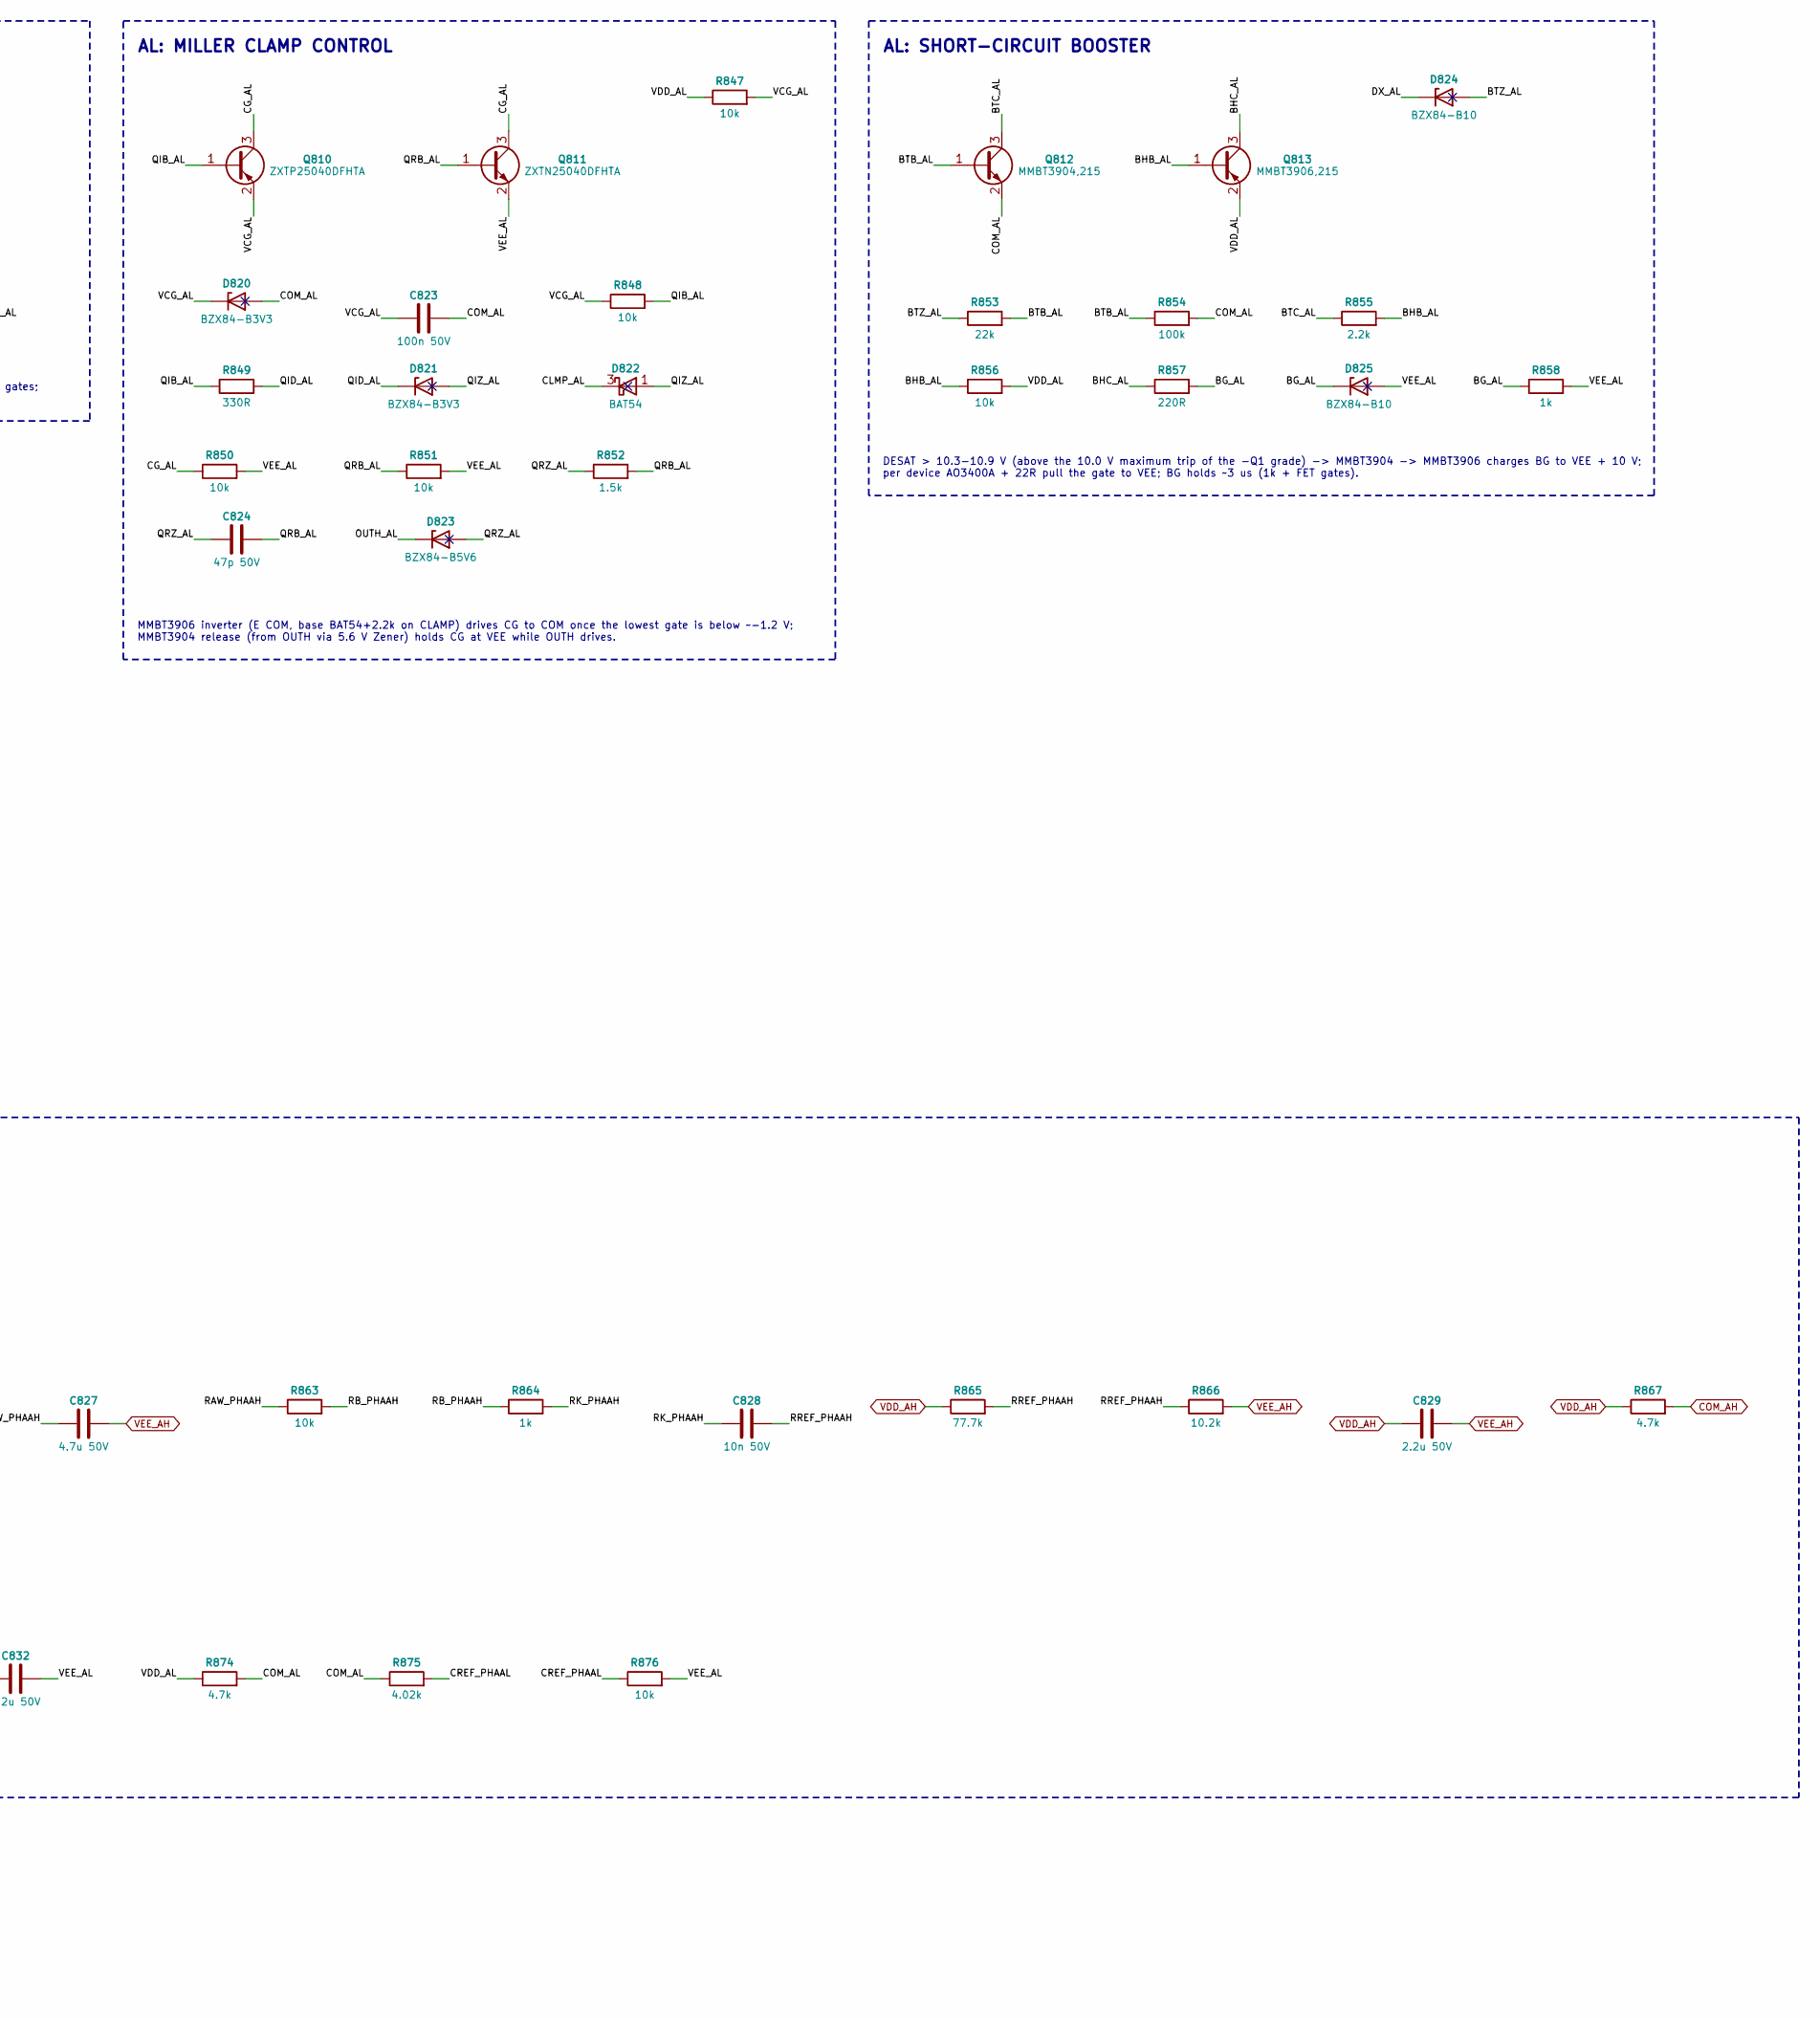
[picture p311: schematic 08_gdal.kicad_sch, part in row 1, column 3]

Parts:
C801, C802, C804: 100p 50V
C803, C805, C807, C810, C823, C826: 100n 50V
C806: 10u 50V
C808, C809: 22u 25V
C811, C813, C815, C817, C819, C821: 1n 50V
C812, C814, C816, C818, C820, C822: 1u 50V
C824: 47p 50V
C825: 10u 16V
C827, C830: 4.7u 50V
C828, C831: 10n 50V
C829, C832: 2.2u 50V
D801, D822, D827: BAT54; MPN BAT54
D802, D805, D808, D811, D814, D817: BZX84-B20,215; MPN BZX84-B20,215
D803, D806, D809, D812, D815, D818: BZX84-B4V7; MPN BZX84-B4V7
D804, D807, D810, D813, D816, D819, D830, D831, D832, D833, D834, D835, D836, D837: PMEG4010CEJ; MPN PMEG4010CEJ
D820, D821: BZX84-B3V3; MPN BZX84-B3V3
D823: BZX84-B5V6; MPN BZX84-B5V6
D824, D825: BZX84-B10; MPN BZX84-B10
D826: BAT54S; MPN BAT54S
D828, D829: BYG23T-M3/TR; MPN BYG23T-M3/TR
Q801, Q802, Q803, Q804, Q805, Q806, Q807: PMV30ENEAR; MPN PMV30ENEAR
Q808, Q809, Q810: ZXTP25040DFHTA; MPN ZXTP25040DFHTA
Q811: ZXTN25040DFHTA; MPN ZXTN25040DFHTA
Q812, Q814: MMBT3904,215; MPN MMBT3904,215
Q813: MMBT3906,215; MPN MMBT3906,215
Q815, Q816: PBSS5540X,135; MPN PBSS5540X,135
R801, R810, R816, R822, R828, R834, R840, R847, R848, R850, R851, R856, R859, R862, R863, R869, R870, R876: 10k
R802, R804, R861: 100R
R803: 3.65k
R805: 0R
R806: 0R; not fitted
R807, R844, R845, R858, R864, R871: 1k
R808, R809, R814, R815, R820, R821, R826, R827, R832, R833, R838, R839: 8.75R
R811, R817, R823, R829, R835, R841: 0.5R
R812, R818, R824, R830, R836, R842: 4.7R
R813, R819, R825, R831, R837, R843: 22R
R846: 150R
R849: 330R
R852: 1.5k
R853: 22k
R854, R860: 100k
R855: 2.2k
R857: 220R
R865, R872: 77.7k
R866, R873: 10.2k
R867, R874: 4.7k
R868, R875: 4.02k
T801: Gate-bias transformer per phase (sim/out/magnetic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
U801: SN74LVC1G17DBVR; MPN SN74LVC1G17DBVR
U802: NSI6651ASC-Q1SWR; MPN NSI6651ASC-Q1SWR
U803: SN6505BDBVR; MPN SN6505BDBVR
U804, U805, U806, U807: ATL431BIDBZR; MPN ATL431BIDBZR

Connections:
+5V: C803.1, C805.1, C825.1, C826.1, T801.2 (CT), U801.5 (VCC), U802.15 (VCC1), U803.2 (VCC)
BG_AL: D825.3 (K), Q807.1 (G), R857.2, R858.1
BHB_AL: Q813.1 (B), R855.2, R856.1
BHC_AL: Q813.3 (C), R857.1
BIAS_EN5: R862.1, U803.5 (EN)
BTB_AL: Q812.1 (B), R853.2, R854.1
BTC_AL: Q812.3 (C), R855.1
BTZ_AL: D824.1 (A), R853.1
CG_AL: Q801.1 (G), Q802.1 (G), Q803.1 (G), Q804.1 (G), Q805.1 (G), Q806.1 (G), Q810.3 (C), Q811.3 (C), R850.1
CLMP_AL: D804.2 (A), D807.2 (A), D810.2 (A), D813.2 (A), D816.2 (A), D819.2 (A), D822.3 (K), R846.2, U802.7 (CLAMP)
COM_AH: R867.2, R868.1, U805.1 (K)
COM_AL: C806.2, C807.2, C808.1, C809.1, C810.1, C823.2, D820.1 (A), D826.1 (A), Q812.2 (E), R806.2, R811.2, R817.2, R823.2, R829.2, R835.2, R841.2, R854.2, R859.1, R874.2, R875.1, U802.3 (GND2), U807.1 (K)
CREF_PHAAH: R868.2, R869.1, U805.2 (REF)
CREF_PHAAL: R875.2, R876.1, U807.2 (REF)
D1_PHA: T801.1 (D1), U803.1 (D1)
D2_PHA: T801.3 (D2), U803.3 (D2)
DS1_AL: D828.1 (K), D829.2 (A)
DTB_AL: R804.1, U801.4 (Y)
DTS_AL: C802.1, D801.3 (K), R803.2, U801.2 (A)
DX_AL: D824.3 (K), D826.3 (COM), D827.3 (K), R861.1, U802.2 (DESAT)
DY_AL: D828.2 (A), R861.2
EN5: U802.14 (~RST/EN)
FLT_N: U802.13 (~FLT)
GND: C801.2, C802.2, C803.2, C804.2, C805.2, C825.2, C826.2, R801.2, R807.2, R862.2, U801.3 (GND), U802.9 (GND1), U803.4 (GND), U803.6 (CLK)
G_AL1: C811.1, D802.3 (K), D804.1 (K), Q801.3 (D), R808.2, R809.2, R810.1, R813.2
G_AL2: C813.1, D805.3 (K), D807.1 (K), Q802.3 (D), R814.2, R815.2, R816.1, R819.2
G_AL3: C815.1, D808.3 (K), D810.1 (K), Q803.3 (D), R820.2, R821.2, R822.1, R825.2
G_AL4: C817.1, D811.3 (K), D813.1 (K), Q804.3 (D), R826.2, R827.2, R828.1, R831.2
G_AL5: C819.1, D814.3 (K), D816.1 (K), Q805.3 (D), R832.2, R833.2, R834.1, R837.2
G_AL6: C821.1, D817.3 (K), D819.1 (K), Q806.3 (D), R838.2, R839.2, R840.1, R843.2
INN_AL: C804.1, R804.2, U802.11 (IN-)
INP_AL: C801.1, R802.2, U802.10 (IN+)
KS_AL1: C811.2, C812.2, D803.3 (K), R810.2, R811.1
KS_AL2: C813.2, C814.2, D806.3 (K), R816.2, R817.1
KS_AL3: C815.2, C816.2, D809.3 (K), R822.2, R823.1
KS_AL4: C817.2, C818.2, D812.3 (K), R828.2, R829.1
KS_AL5: C819.2, C820.2, D815.3 (K), R834.2, R835.1
KS_AL6: C821.2, C822.2, D818.3 (K), R840.2, R841.1
NDB_AL: Q814.1 (B), R859.2
NDX_AL: D827.1 (A), Q814.3 (C), R860.2
OUTH_AL: D823.3 (K), R808.1, R814.1, R820.1, R826.1, R832.1, R838.1, R846.1, U802.4 (OUTH)
OUTL_AL: Q808.1 (B), Q809.1 (B), R844.1, R845.1, U802.6 (OUTL)
P1_AL: R805.1, R806.1, U802.1 (VEE2)
P16_AL: R807.1, U802.16 (TEST)
PWM1_5V: D801.1 (A), R803.1
PWM2_5V: R801.1, R802.1
QIB_AL: Q810.1 (B), R848.2, R849.1
QID_AL: D821.3 (K), R849.2
QIZ_AL: D821.1 (A), D822.1 (A)
QRB_AL: C824.2, Q811.1 (B), R851.1, R852.2
QRZ_AL: C824.1, D823.1 (A), R852.1
RAW_PHAAH: C827.1, D830.1 (K), D831.1 (K), Q815.1 (E), R863.1
RAW_PHAAL: C830.1, D834.1 (K), D835.1 (K), Q816.1 (E), R870.1
RB_PHAAH: Q815.3 (B), R863.2, R864.1
RB_PHAAL: Q816.3 (B), R870.2, R871.1
RDY: U802.12 (RDY)
RK_PHAAH: C828.1, R864.2, U804.1 (K)
RK_PHAAL: C831.1, R871.2, U806.1 (K)
RREF_PHAAH: C828.2, R865.2, R866.1, U804.2 (REF)
RREF_PHAAL: C831.2, R872.2, R873.1, U806.2 (REF)
SA_PHAAH: D830.2 (A), D832.1 (K), T801.4 (S1A)
SA_PHAAL: D834.2 (A), D836.1 (K), T801.6 (S2A)
SB_AL: Q807.3 (D), R813.1, R819.1, R825.1, R831.1, R837.1, R843.1
SB_PHAAH: D831.2 (A), D833.1 (K), T801.5 (S1B)
SB_PHAAL: D835.2 (A), D837.1 (K), T801.7 (S2B)
SK1_AL: Q808.2 (E), R809.1, R815.1, R821.1, R844.2
SK2_AL: Q809.2 (E), R827.1, R833.1, R839.1, R845.2
SW_A: D829.1 (K)
VCG_AL: C823.1, D820.3 (K), Q810.2 (E), R847.2, R848.1
VDD_AH: C829.1, Q815.2 (C), R865.1, R867.1
VDD_AL: C806.1, C807.1, C832.1, D826.2 (K), Q813.2 (E), Q816.2 (C), R847.1, R856.2, R860.1, R872.1, R874.1, U802.5 (VCC2)
VEEL1_AL: C812.1, Q801.2 (S), R812.2
VEEL2_AL: C814.1, Q802.2 (S), R818.2
VEEL3_AL: C816.1, Q803.2 (S), R824.2
VEEL4_AL: C818.1, Q804.2 (S), R830.2
VEEL5_AL: C820.1, Q805.2 (S), R836.2
VEEL6_AL: C822.1, Q806.2 (S), R842.2
VEE_AH: C827.2, C829.2, D832.2 (A), D833.2 (A), R866.2, R869.2, U804.3 (A), U805.3 (A)
VEE_AL: C808.2, C809.2, C810.2, C830.2, C832.2, D825.1 (A), D836.2 (A), D837.2 (A), Q807.2 (S), Q808.3 (C), Q809.3 (C), Q811.2 (E), Q814.2 (E), R805.2, R812.1, R818.1, R824.1, R830.1, R836.1, R842.1, R850.2, R851.2, R858.2, R873.2, R876.2, U802.8 (VEE2), U806.3 (A), U807.3 (A)
ZM1_AL: D802.1 (A), D803.1 (A)
ZM2_AL: D805.1 (A), D806.1 (A)
ZM3_AL: D808.1 (A), D809.1 (A)
ZM4_AL: D811.1 (A), D812.1 (A)
ZM5_AL: D814.1 (A), D815.1 (A)
ZM6_AL: D817.1 (A), D818.1 (A)

Notes on the sheet:
Gate and Kelvin of each device as coupled pairs of equal length from the COM star; Ron, Roff, Kelvin R, 10k + 1n, Zeners and the clamp FET + C_VL at each device (loop <= 1 nH). PNP followers next to their three gates. DESAT string >= 2.5 mm pad gap per diode; coat to PD1. Miller hold of six gates N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
AL: LOGIC SIDE
AL: DRIVER AND 6 GATES
AL: SHORT-CIRCUIT BOOSTER
IN+ = own PWM; IN- = complementary switch, falling edge stretched 3.65k/100p (interlock + min dead time = max(firmware, hardware)). Bias PG (active low) pulls RDY low.
LEG A: LAYOUT RULES
AL: DESAT
DESAT pin (internal 500 uA blanking source, trip 8.5-10.0 V) - Rs - 2 x BYG23T-M3/TR (1300 V each) - drain. BAT54S keeps DX between COM and VDD against dv/dt through the string; Cblk footprint DNP.
SN6505B push-pull 420 kHz from +5V, BIAS_EN high = on; T_BIAS4 custom, functional insulation (PD-free >= 1.75 kVpk, <= 5 pF per secondary). Per channel: bridge, PNP regulator VDD-VEE, ATL431 COM split.
DESAT > 10.3-10.9 V (above the 10.0 V maximum trip of the -Q1 grade) -> MMBT3904 -> MMBT3906 charges BG to VEE + 10 V; per device AO3400A + 22R pull the gate to VEE; BG holds ~3 us (1k + FET gates).
2 x ZXTP25040DFH emitter followers on OUTL (B-E 1k, C to VEE): each sinks the Roff current of 3 gates; the NSI6651 supplies base current only. Turn-on stays on OUTH.
Per device: Ron/Roff, 0.5R Kelvin R to the COM star, 10k and Zeners (about +21 V / -5.7 V) on its own Kelvin net. Miller hold: N-MOSFET clamp (PMV30ENEA) gate-pin to a local VEE (1u on the Kelvin pin). LAYOUT: FET + 1u at the device, loop <= 1 nH.
AL: TURN-OFF BUFFER
PHA: GATE BIAS (PER PHASE)
AL: MILLER CLAMP CONTROL
MMBT3906 inverter (E COM, base BAT54+2.2k on CLAMP) drives CG to COM once the lowest gate is below ~-1.2 V; MMBT3904 release (from OUTH via 5.6 V Zener) holds CG at VEE while OUTH drives.
