vectivolt/PCM/hardware/PCS-PWR-4W/sheets/09_gdbh.kicad_sch

## KiCad design hardware/PCS-PWR-4W/sheets/09_gdbh.kicad_sch (2026-10-07)

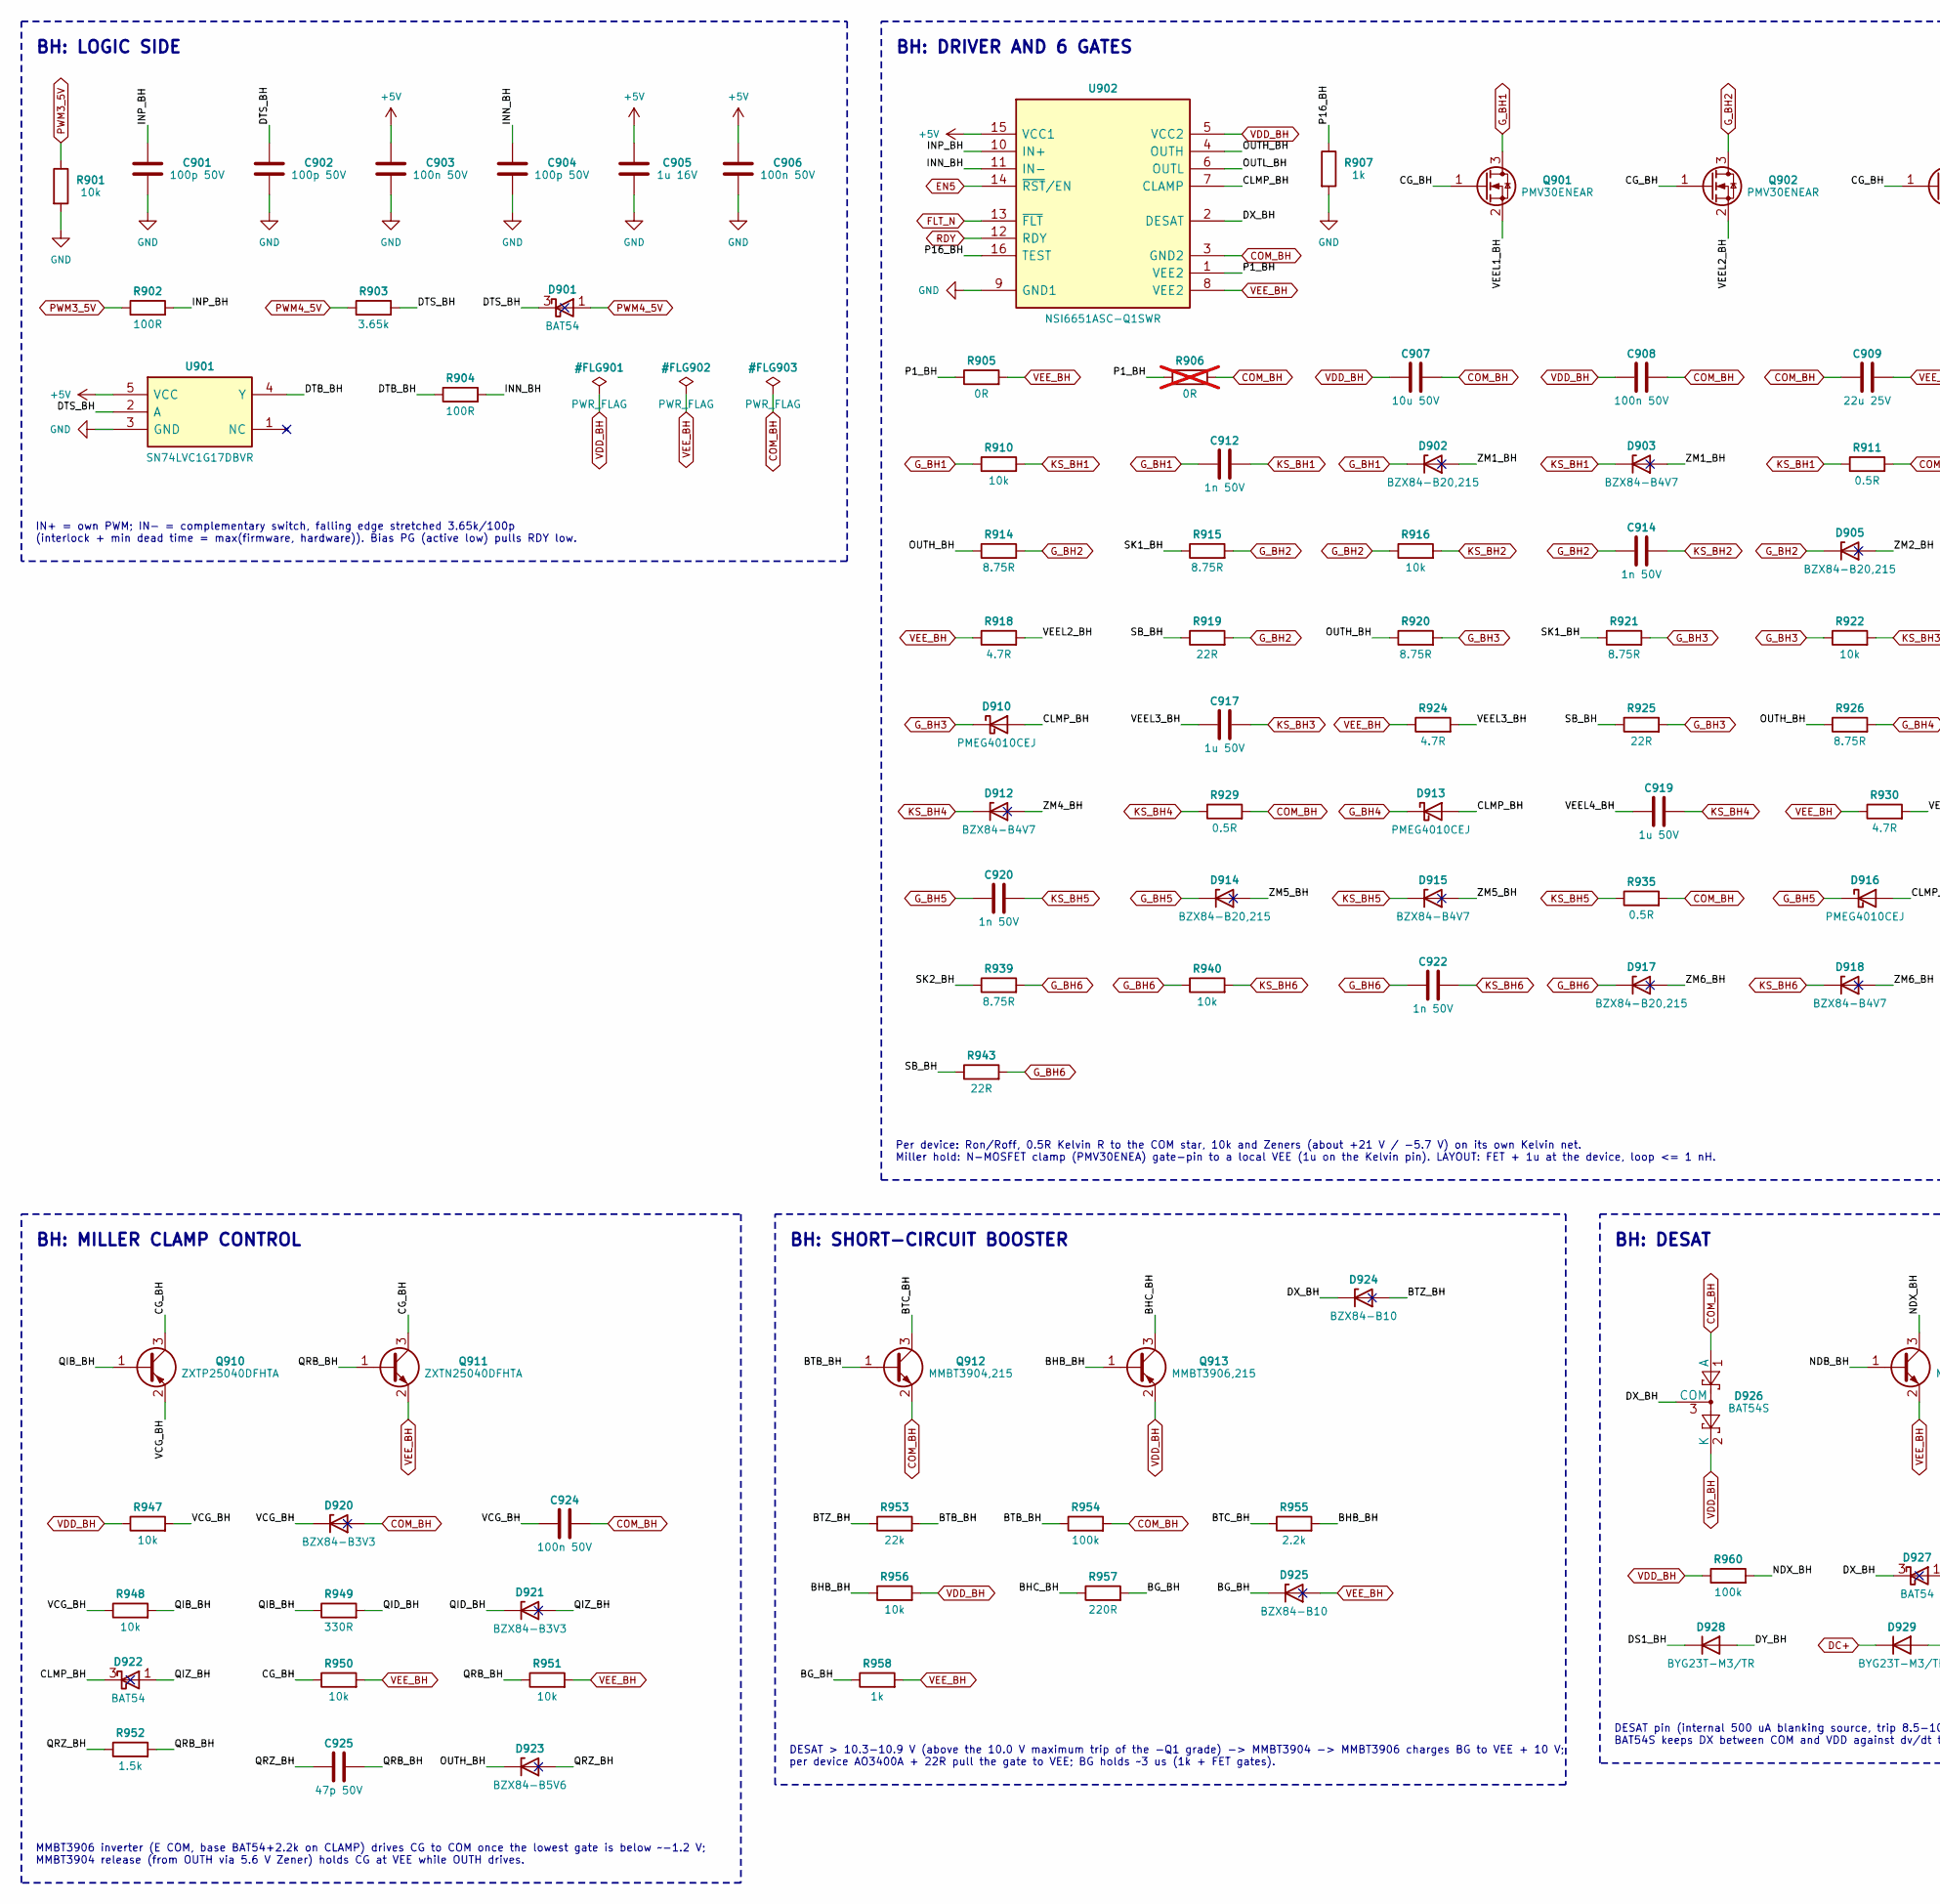
[picture p312: schematic 09_gdbh.kicad_sch, part in row 1, column 1]

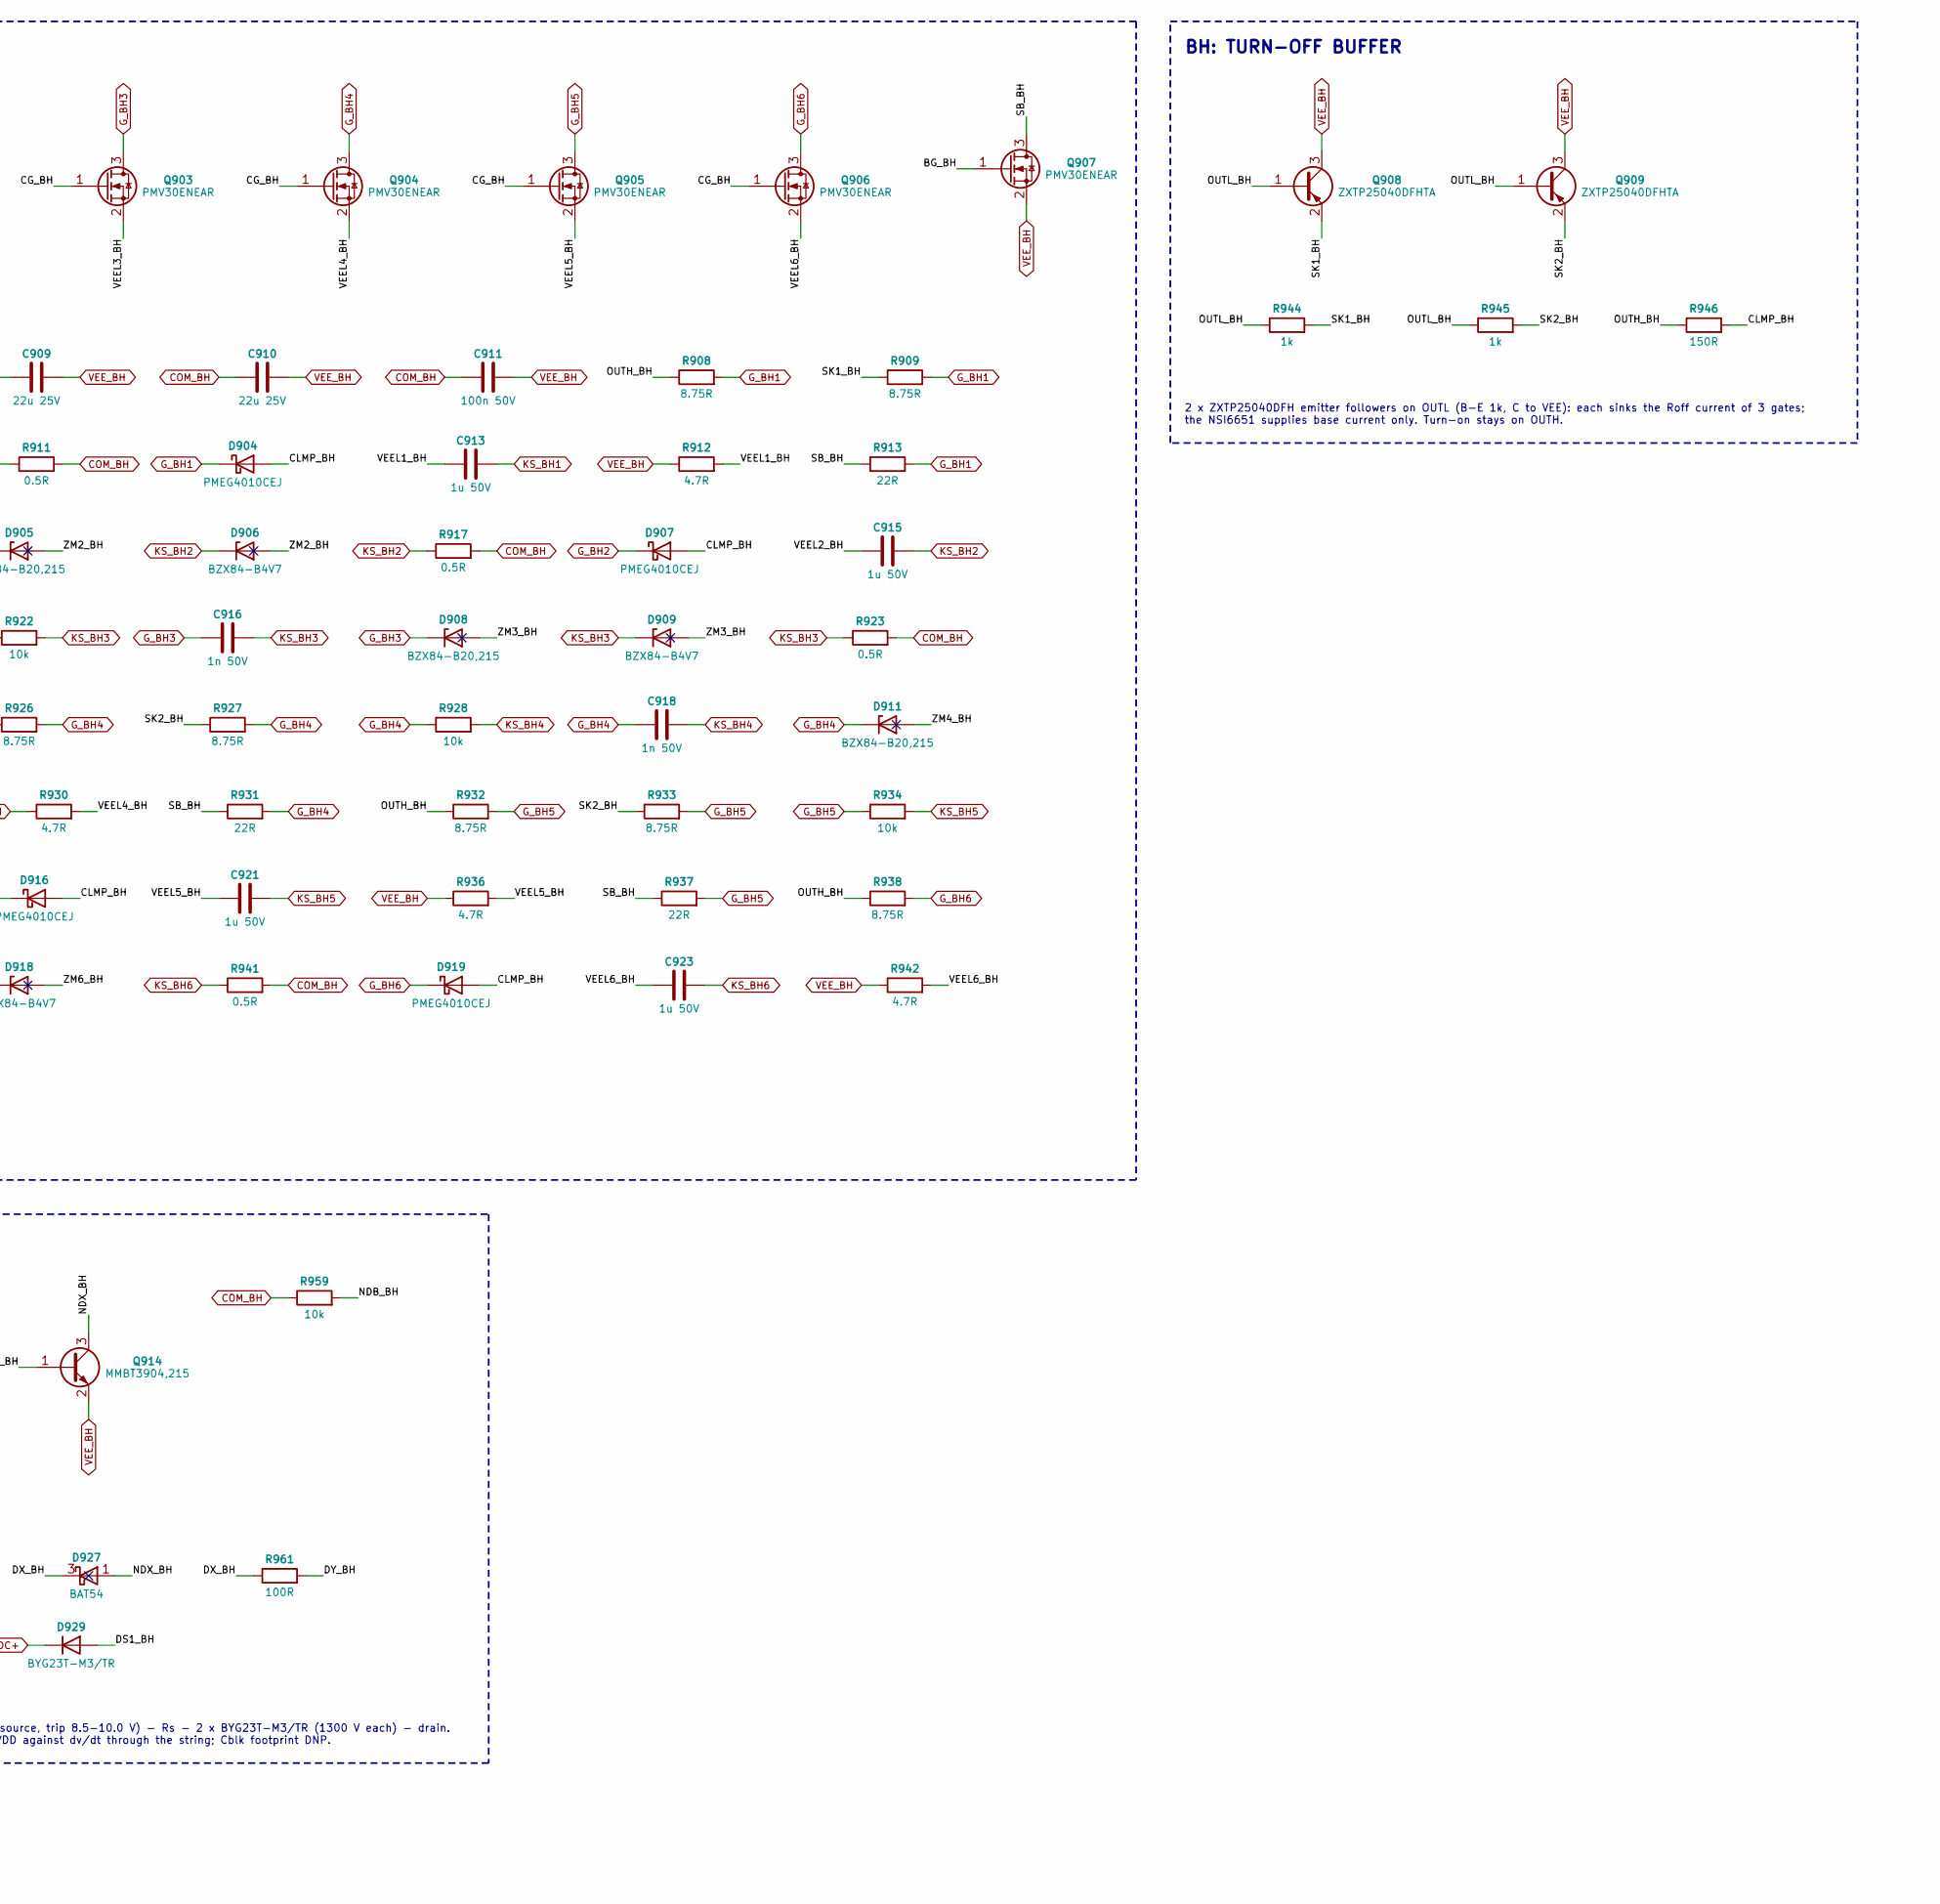
[picture p313: schematic 09_gdbh.kicad_sch, part in row 1, column 2]

Parts:
C901, C902, C904: 100p 50V
C903, C906, C908, C911, C924: 100n 50V
C905: 1u 16V
C907: 10u 50V
C909, C910: 22u 25V
C912, C914, C916, C918, C920, C922: 1n 50V
C913, C915, C917, C919, C921, C923: 1u 50V
C925: 47p 50V
D901, D922, D927: BAT54; MPN BAT54
D902, D905, D908, D911, D914, D917: BZX84-B20,215; MPN BZX84-B20,215
D903, D906, D909, D912, D915, D918: BZX84-B4V7; MPN BZX84-B4V7
D904, D907, D910, D913, D916, D919: PMEG4010CEJ; MPN PMEG4010CEJ
D920, D921: BZX84-B3V3; MPN BZX84-B3V3
D923: BZX84-B5V6; MPN BZX84-B5V6
D924, D925: BZX84-B10; MPN BZX84-B10
D926: BAT54S; MPN BAT54S
D928, D929: BYG23T-M3/TR; MPN BYG23T-M3/TR
Q901, Q902, Q903, Q904, Q905, Q906, Q907: PMV30ENEAR; MPN PMV30ENEAR
Q908, Q909, Q910: ZXTP25040DFHTA; MPN ZXTP25040DFHTA
Q911: ZXTN25040DFHTA; MPN ZXTN25040DFHTA
Q912, Q914: MMBT3904,215; MPN MMBT3904,215
Q913: MMBT3906,215; MPN MMBT3906,215
R901, R910, R916, R922, R928, R934, R940, R947, R948, R950, R951, R956, R959: 10k
R902, R904, R961: 100R
R903: 3.65k
R905: 0R
R906: 0R; not fitted
R907, R944, R945, R958: 1k
R908, R909, R914, R915, R920, R921, R926, R927, R932, R933, R938, R939: 8.75R
R911, R917, R923, R929, R935, R941: 0.5R
R912, R918, R924, R930, R936, R942: 4.7R
R913, R919, R925, R931, R937, R943: 22R
R946: 150R
R949: 330R
R952: 1.5k
R953: 22k
R954, R960: 100k
R955: 2.2k
R957: 220R
U901: SN74LVC1G17DBVR; MPN SN74LVC1G17DBVR
U902: NSI6651ASC-Q1SWR; MPN NSI6651ASC-Q1SWR

Connections:
+5V: C903.1, C905.1, C906.1, U901.5 (VCC), U902.15 (VCC1)
BG_BH: D925.3 (K), Q907.1 (G), R957.2, R958.1
BHB_BH: Q913.1 (B), R955.2, R956.1
BHC_BH: Q913.3 (C), R957.1
BTB_BH: Q912.1 (B), R953.2, R954.1
BTC_BH: Q912.3 (C), R955.1
BTZ_BH: D924.1 (A), R953.1
CG_BH: Q901.1 (G), Q902.1 (G), Q903.1 (G), Q904.1 (G), Q905.1 (G), Q906.1 (G), Q910.3 (C), Q911.3 (C), R950.1
CLMP_BH: D904.2 (A), D907.2 (A), D910.2 (A), D913.2 (A), D916.2 (A), D919.2 (A), D922.3 (K), R946.2, U902.7 (CLAMP)
COM_BH: C907.2, C908.2, C909.1, C910.1, C911.1, C924.2, D920.1 (A), D926.1 (A), Q912.2 (E), R906.2, R911.2, R917.2, R923.2, R929.2, R935.2, R941.2, R954.2, R959.1, U902.3 (GND2)
DC+: D929.1 (K)
DS1_BH: D928.1 (K), D929.2 (A)
DTB_BH: R904.1, U901.4 (Y)
DTS_BH: C902.1, D901.3 (K), R903.2, U901.2 (A)
DX_BH: D924.3 (K), D926.3 (COM), D927.3 (K), R961.1, U902.2 (DESAT)
DY_BH: D928.2 (A), R961.2
EN5: U902.14 (~RST/EN)
FLT_N: U902.13 (~FLT)
GND: C901.2, C902.2, C903.2, C904.2, C905.2, C906.2, R901.2, R907.2, U901.3 (GND), U902.9 (GND1)
G_BH1: C912.1, D902.3 (K), D904.1 (K), Q901.3 (D), R908.2, R909.2, R910.1, R913.2
G_BH2: C914.1, D905.3 (K), D907.1 (K), Q902.3 (D), R914.2, R915.2, R916.1, R919.2
G_BH3: C916.1, D908.3 (K), D910.1 (K), Q903.3 (D), R920.2, R921.2, R922.1, R925.2
G_BH4: C918.1, D911.3 (K), D913.1 (K), Q904.3 (D), R926.2, R927.2, R928.1, R931.2
G_BH5: C920.1, D914.3 (K), D916.1 (K), Q905.3 (D), R932.2, R933.2, R934.1, R937.2
G_BH6: C922.1, D917.3 (K), D919.1 (K), Q906.3 (D), R938.2, R939.2, R940.1, R943.2
INN_BH: C904.1, R904.2, U902.11 (IN-)
INP_BH: C901.1, R902.2, U902.10 (IN+)
KS_BH1: C912.2, C913.2, D903.3 (K), R910.2, R911.1
KS_BH2: C914.2, C915.2, D906.3 (K), R916.2, R917.1
KS_BH3: C916.2, C917.2, D909.3 (K), R922.2, R923.1
KS_BH4: C918.2, C919.2, D912.3 (K), R928.2, R929.1
KS_BH5: C920.2, C921.2, D915.3 (K), R934.2, R935.1
KS_BH6: C922.2, C923.2, D918.3 (K), R940.2, R941.1
NDB_BH: Q914.1 (B), R959.2
NDX_BH: D927.1 (A), Q914.3 (C), R960.2
OUTH_BH: D923.3 (K), R908.1, R914.1, R920.1, R926.1, R932.1, R938.1, R946.1, U902.4 (OUTH)
OUTL_BH: Q908.1 (B), Q909.1 (B), R944.1, R945.1, U902.6 (OUTL)
P1_BH: R905.1, R906.1, U902.1 (VEE2)
P16_BH: R907.1, U902.16 (TEST)
PWM3_5V: R901.1, R902.1
PWM4_5V: D901.1 (A), R903.1
QIB_BH: Q910.1 (B), R948.2, R949.1
QID_BH: D921.3 (K), R949.2
QIZ_BH: D921.1 (A), D922.1 (A)
QRB_BH: C925.2, Q911.1 (B), R951.1, R952.2
QRZ_BH: C925.1, D923.1 (A), R952.1
RDY: U902.12 (RDY)
SB_BH: Q907.3 (D), R913.1, R919.1, R925.1, R931.1, R937.1, R943.1
SK1_BH: Q908.2 (E), R909.1, R915.1, R921.1, R944.2
SK2_BH: Q909.2 (E), R927.1, R933.1, R939.1, R945.2
VCG_BH: C924.1, D920.3 (K), Q910.2 (E), R947.2, R948.1
VDD_BH: C907.1, C908.1, D926.2 (K), Q913.2 (E), R947.1, R956.2, R960.1, U902.5 (VCC2)
VEEL1_BH: C913.1, Q901.2 (S), R912.2
VEEL2_BH: C915.1, Q902.2 (S), R918.2
VEEL3_BH: C917.1, Q903.2 (S), R924.2
VEEL4_BH: C919.1, Q904.2 (S), R930.2
VEEL5_BH: C921.1, Q905.2 (S), R936.2
VEEL6_BH: C923.1, Q906.2 (S), R942.2
VEE_BH: C909.2, C910.2, C911.2, D925.1 (A), Q907.2 (S), Q908.3 (C), Q909.3 (C), Q911.2 (E), Q914.2 (E), R905.2, R912.1, R918.1, R924.1, R930.1, R936.1, R942.1, R950.2, R951.2, R958.2, U902.8 (VEE2)
ZM1_BH: D902.1 (A), D903.1 (A)
ZM2_BH: D905.1 (A), D906.1 (A)
ZM3_BH: D908.1 (A), D909.1 (A)
ZM4_BH: D911.1 (A), D912.1 (A)
ZM5_BH: D914.1 (A), D915.1 (A)
ZM6_BH: D917.1 (A), D918.1 (A)

Notes on the sheet:
BH: LOGIC SIDE
2 x ZXTP25040DFH emitter followers on OUTL (B-E 1k, C to VEE): each sinks the Roff current of 3 gates; the NSI6651 supplies base current only. Turn-on stays on OUTH.
BH: SHORT-CIRCUIT BOOSTER
DESAT > 10.3-10.9 V (above the 10.0 V maximum trip of the -Q1 grade) -> MMBT3904 -> MMBT3906 charges BG to VEE + 10 V; per device AO3400A + 22R pull the gate to VEE; BG holds ~3 us (1k + FET gates).
BH: DESAT
BH: DRIVER AND 6 GATES
BH: TURN-OFF BUFFER
DESAT pin (internal 500 uA blanking source, trip 8.5-10.0 V) - Rs - 2 x BYG23T-M3/TR (1300 V each) - drain. BAT54S keeps DX between COM and VDD against dv/dt through the string; Cblk footprint DNP.
MMBT3906 inverter (E COM, base BAT54+2.2k on CLAMP) drives CG to COM once the lowest gate is below ~-1.2 V; MMBT3904 release (from OUTH via 5.6 V Zener) holds CG at VEE while OUTH drives.
BH: MILLER CLAMP CONTROL
IN+ = own PWM; IN- = complementary switch, falling edge stretched 3.65k/100p (interlock + min dead time = max(firmware, hardware)). Bias PG (active low) pulls RDY low.
Per device: Ron/Roff, 0.5R Kelvin R to the COM star, 10k and Zeners (about +21 V / -5.7 V) on its own Kelvin net. Miller hold: N-MOSFET clamp (PMV30ENEA) gate-pin to a local VEE (1u on the Kelvin pin). LAYOUT: FET + 1u at the device, loop <= 1 nH.
