vectivolt/PCM/hardware/PCS-PWR-4W/sheets/10_gdbl.kicad_sch

## KiCad design hardware/PCS-PWR-4W/sheets/10_gdbl.kicad_sch (2026-10-07)

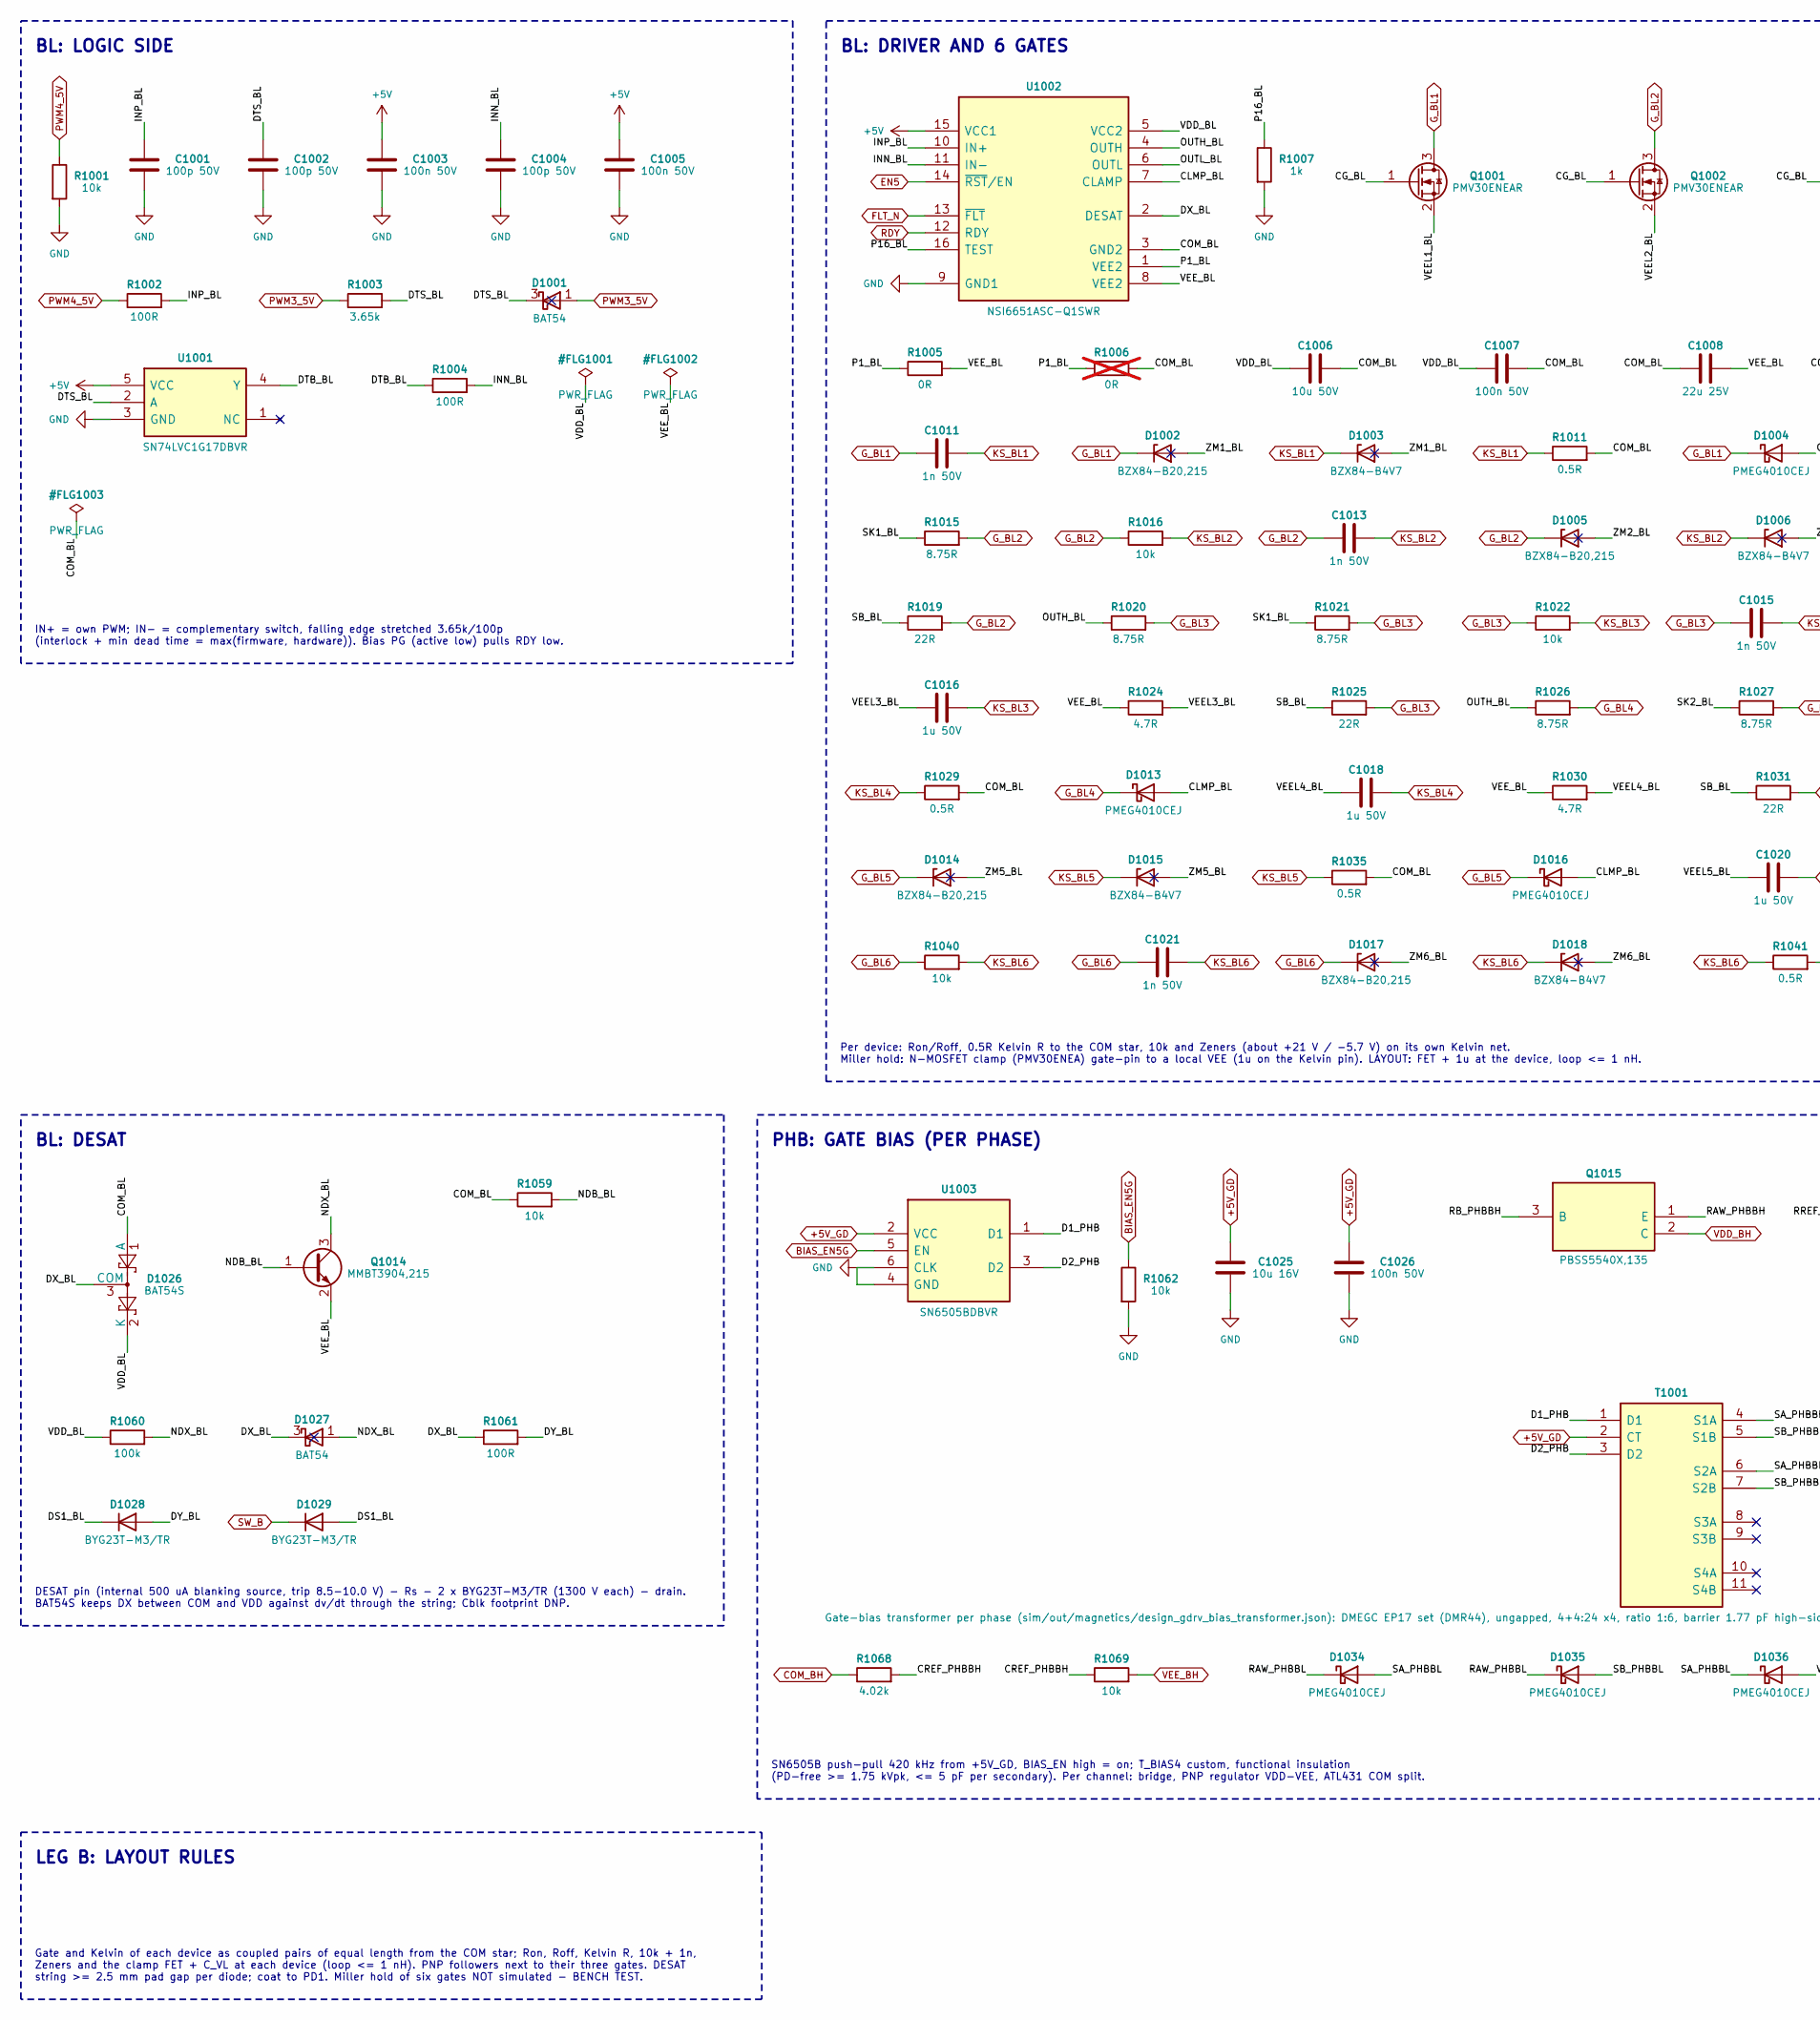
[picture p314: schematic 10_gdbl.kicad_sch, part in row 1, column 1]

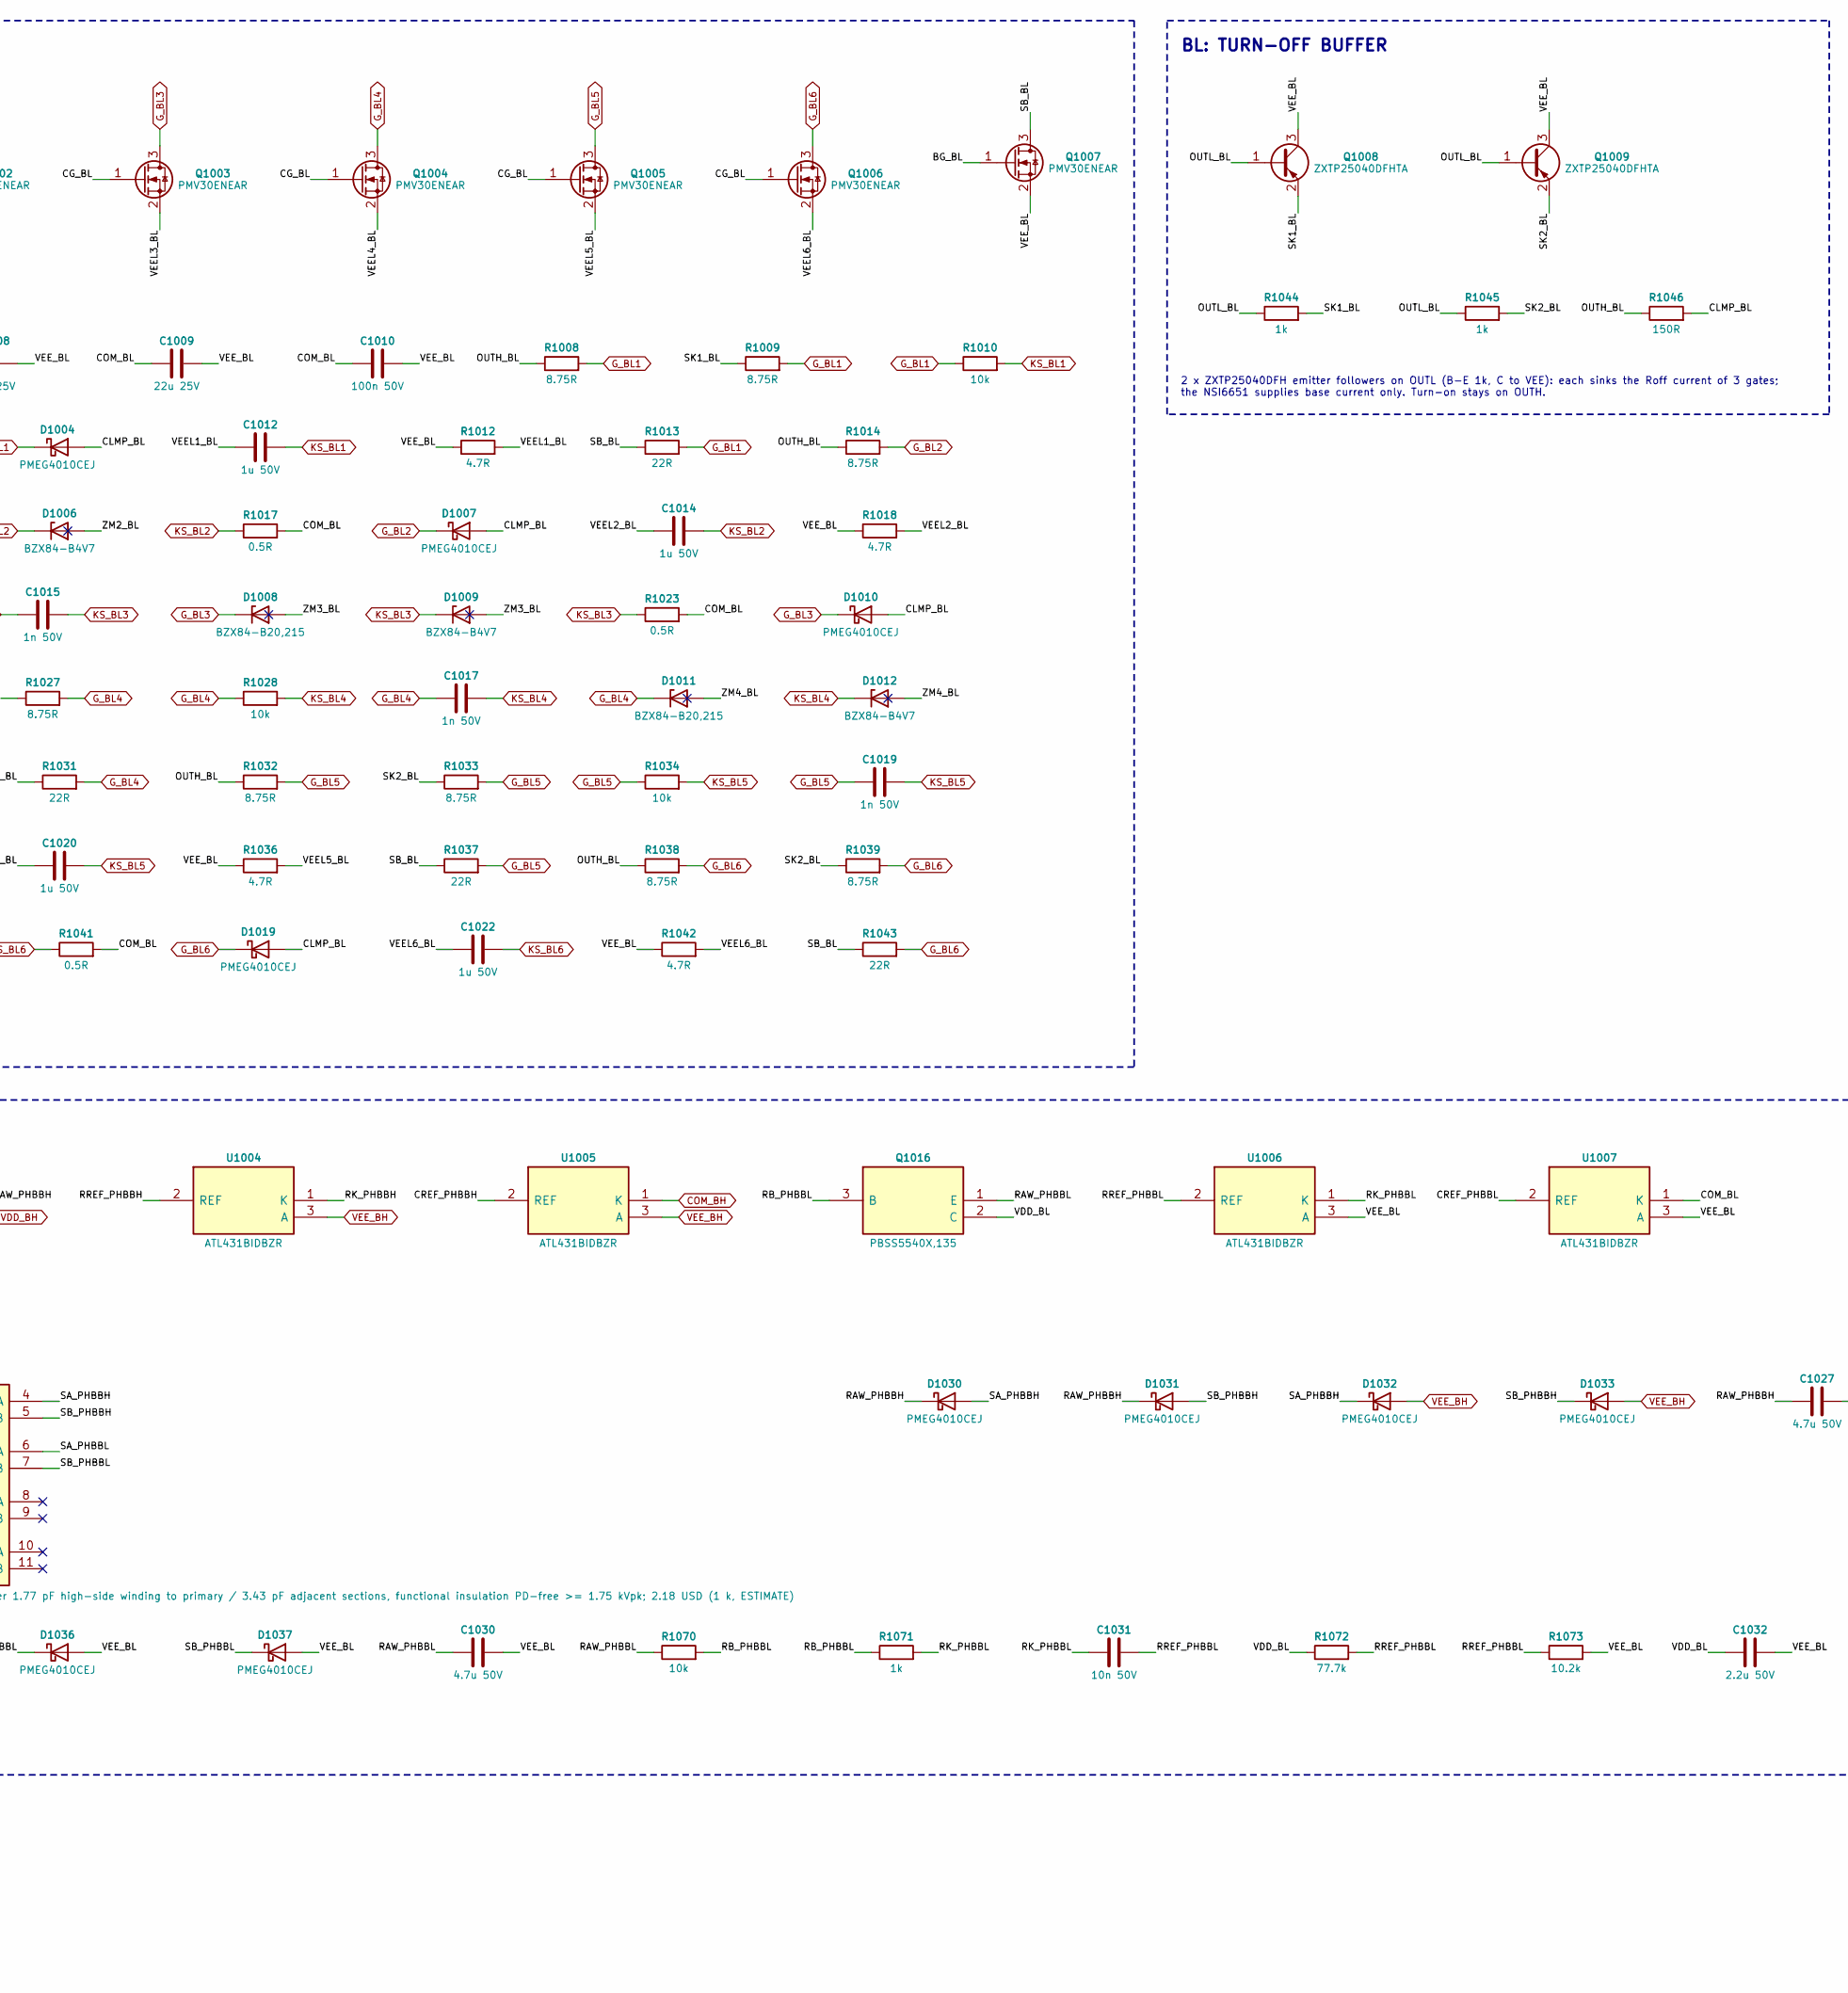
[picture p315: schematic 10_gdbl.kicad_sch, part in row 1, column 2]

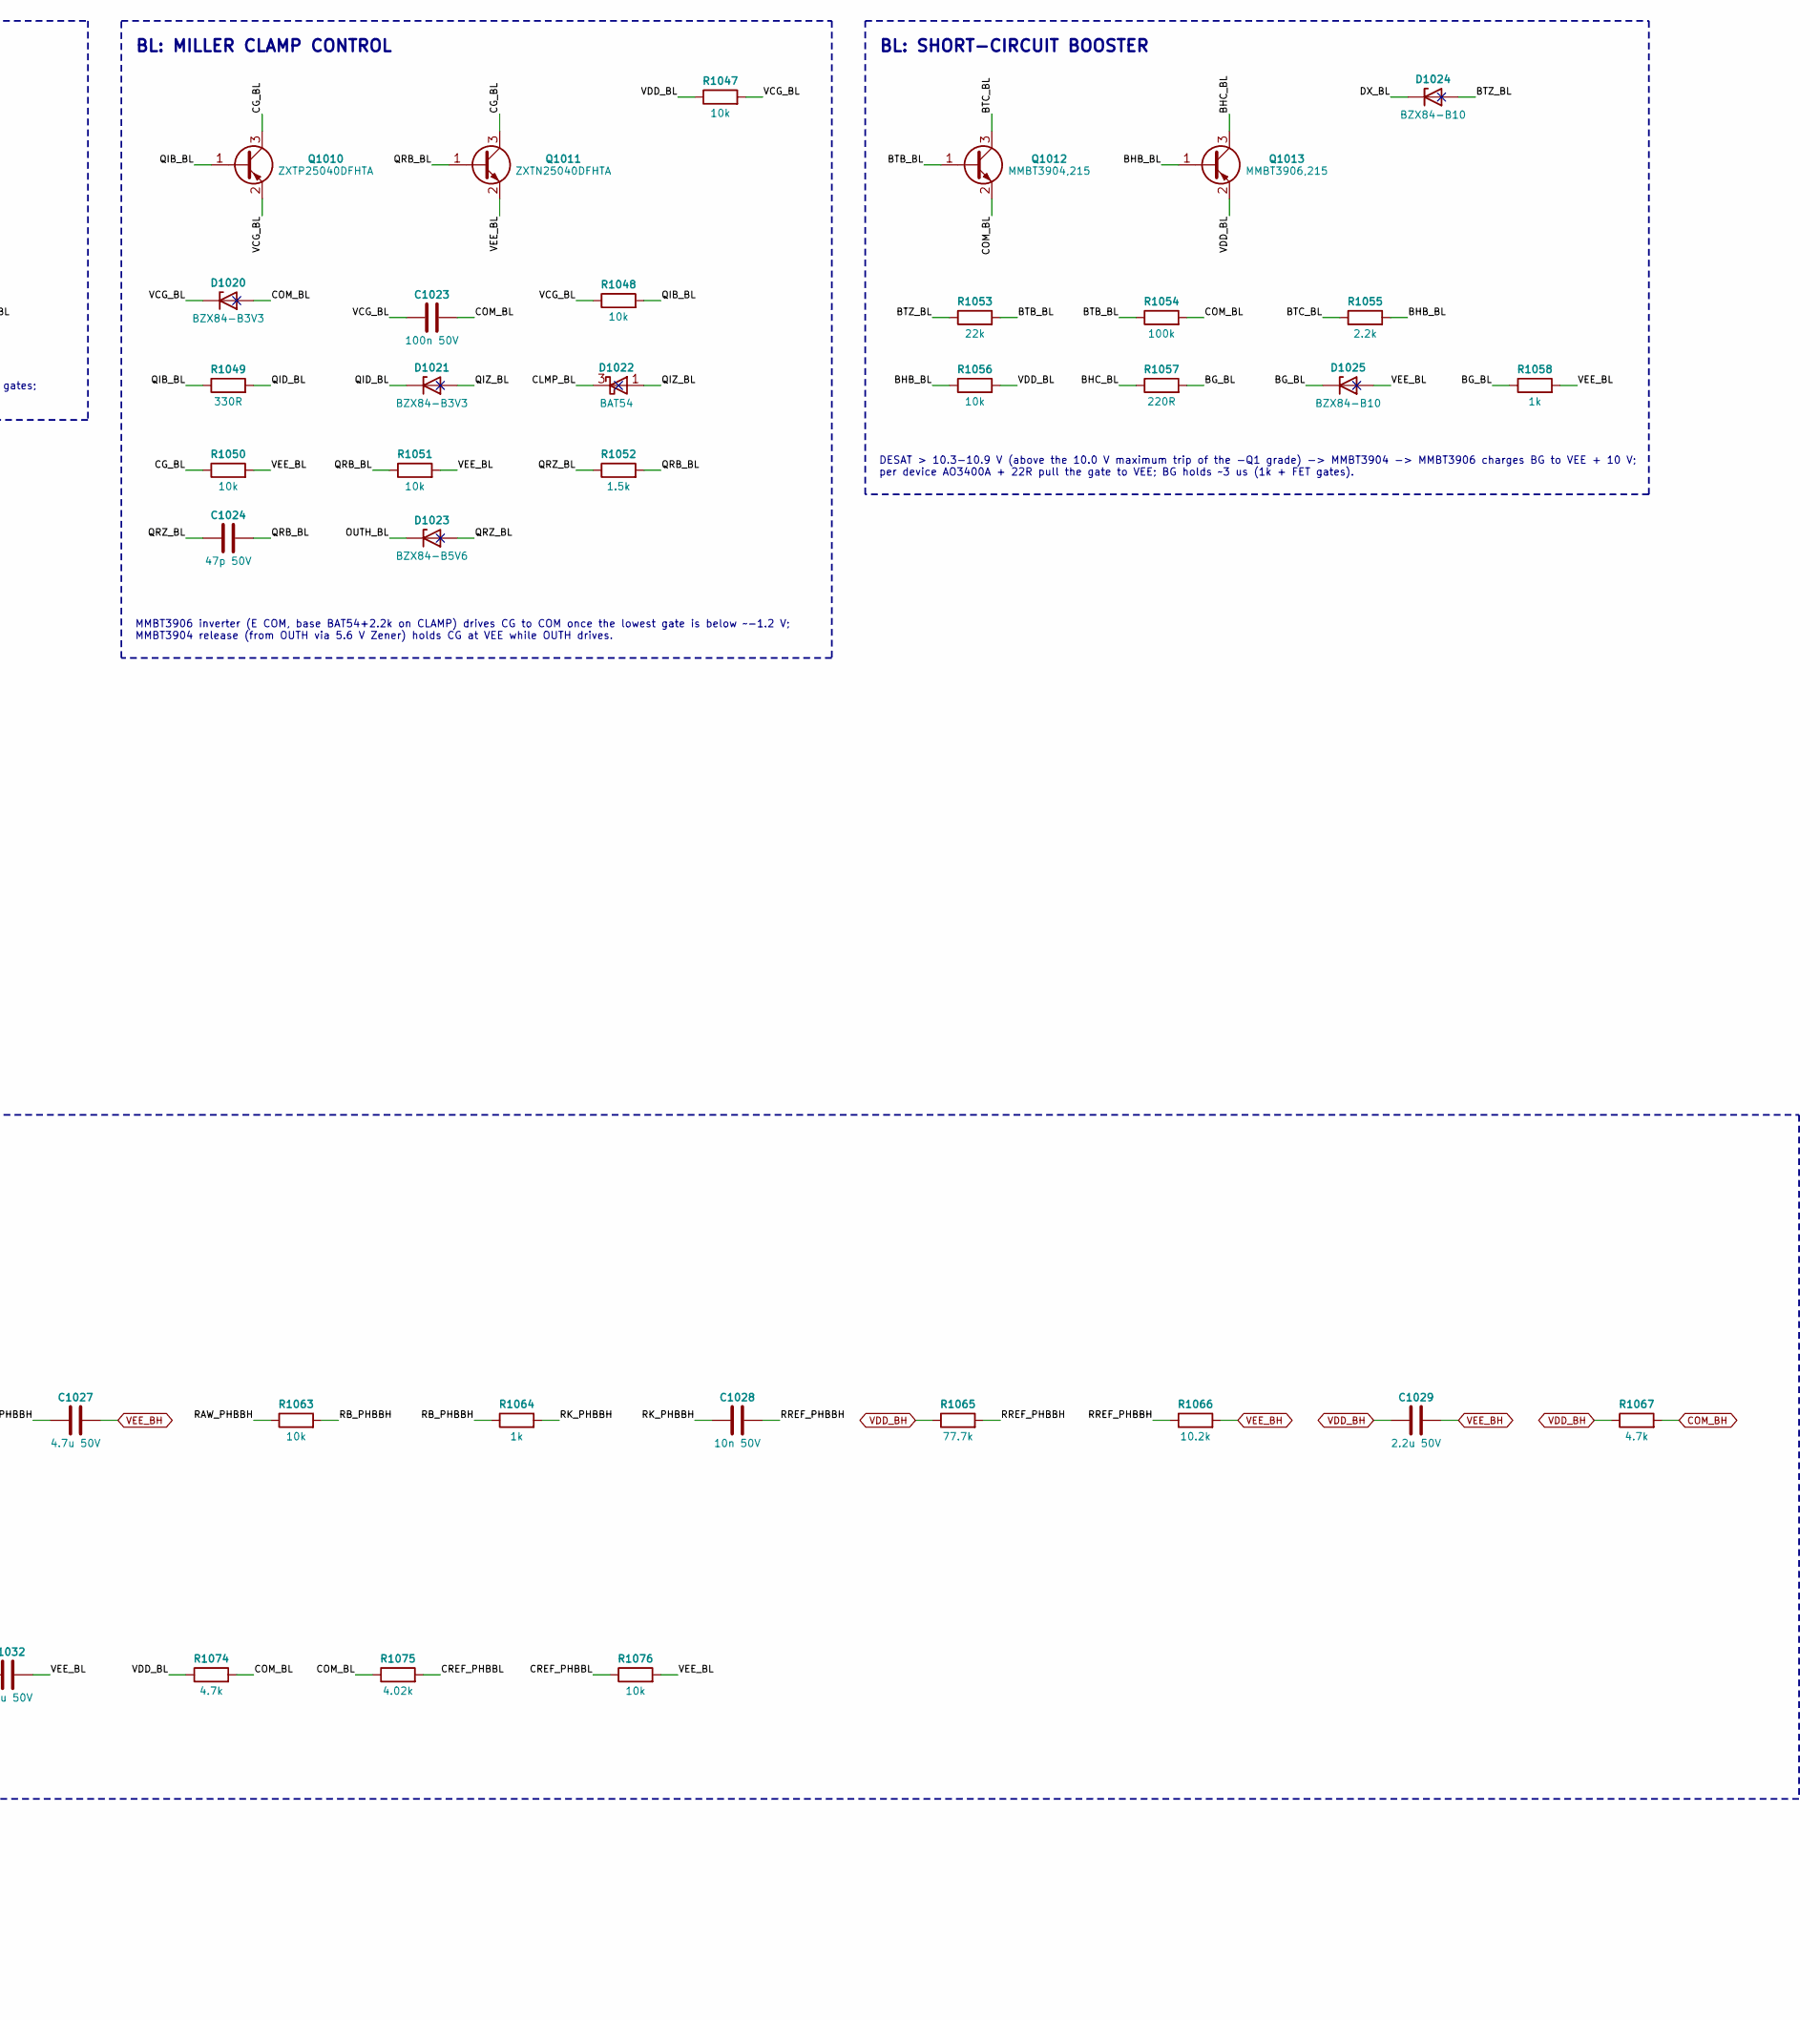
[picture p316: schematic 10_gdbl.kicad_sch, part in row 1, column 3]

Parts:
C1001, C1002, C1004: 100p 50V
C1003, C1005, C1007, C1010, C1023, C1026: 100n 50V
C1006: 10u 50V
C1008, C1009: 22u 25V
C1011, C1013, C1015, C1017, C1019, C1021: 1n 50V
C1012, C1014, C1016, C1018, C1020, C1022: 1u 50V
C1024: 47p 50V
C1025: 10u 16V
C1027, C1030: 4.7u 50V
C1028, C1031: 10n 50V
C1029, C1032: 2.2u 50V
D1001, D1022, D1027: BAT54; MPN BAT54
D1002, D1005, D1008, D1011, D1014, D1017: BZX84-B20,215; MPN BZX84-B20,215
D1003, D1006, D1009, D1012, D1015, D1018: BZX84-B4V7; MPN BZX84-B4V7
D1004, D1007, D1010, D1013, D1016, D1019, D1030, D1031, D1032, D1033, D1034, D1035, D1036, D1037: PMEG4010CEJ; MPN PMEG4010CEJ
D1020, D1021: BZX84-B3V3; MPN BZX84-B3V3
D1023: BZX84-B5V6; MPN BZX84-B5V6
D1024, D1025: BZX84-B10; MPN BZX84-B10
D1026: BAT54S; MPN BAT54S
D1028, D1029: BYG23T-M3/TR; MPN BYG23T-M3/TR
Q1001, Q1002, Q1003, Q1004, Q1005, Q1006, Q1007: PMV30ENEAR; MPN PMV30ENEAR
Q1008, Q1009, Q1010: ZXTP25040DFHTA; MPN ZXTP25040DFHTA
Q1011: ZXTN25040DFHTA; MPN ZXTN25040DFHTA
Q1012, Q1014: MMBT3904,215; MPN MMBT3904,215
Q1013: MMBT3906,215; MPN MMBT3906,215
Q1015, Q1016: PBSS5540X,135; MPN PBSS5540X,135
R1001, R1010, R1016, R1022, R1028, R1034, R1040, R1047, R1048, R1050, R1051, R1056, R1059, R1062, R1063, R1069, R1070, R1076: 10k
R1002, R1004, R1061: 100R
R1003: 3.65k
R1005: 0R
R1006: 0R; not fitted
R1007, R1044, R1045, R1058, R1064, R1071: 1k
R1008, R1009, R1014, R1015, R1020, R1021, R1026, R1027, R1032, R1033, R1038, R1039: 8.75R
R1011, R1017, R1023, R1029, R1035, R1041: 0.5R
R1012, R1018, R1024, R1030, R1036, R1042: 4.7R
R1013, R1019, R1025, R1031, R1037, R1043: 22R
R1046: 150R
R1049: 330R
R1052: 1.5k
R1053: 22k
R1054, R1060: 100k
R1055: 2.2k
R1057: 220R
R1065, R1072: 77.7k
R1066, R1073: 10.2k
R1067, R1074: 4.7k
R1068, R1075: 4.02k
T1001: Gate-bias transformer per phase (sim/out/magnetic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
U1001: SN74LVC1G17DBVR; MPN SN74LVC1G17DBVR
U1002: NSI6651ASC-Q1SWR; MPN NSI6651ASC-Q1SWR
U1003: SN6505BDBVR; MPN SN6505BDBVR
U1004, U1005, U1006, U1007: ATL431BIDBZR; MPN ATL431BIDBZR

Connections:
+5V: C1003.1, C1005.1, U1001.5 (VCC), U1002.15 (VCC1)
+5V_GD: C1025.1, C1026.1, T1001.2 (CT), U1003.2 (VCC)
BG_BL: D1025.3 (K), Q1007.1 (G), R1057.2, R1058.1
BHB_BL: Q1013.1 (B), R1055.2, R1056.1
BHC_BL: Q1013.3 (C), R1057.1
BIAS_EN5G: R1062.1, U1003.5 (EN)
BTB_BL: Q1012.1 (B), R1053.2, R1054.1
BTC_BL: Q1012.3 (C), R1055.1
BTZ_BL: D1024.1 (A), R1053.1
CG_BL: Q1001.1 (G), Q1002.1 (G), Q1003.1 (G), Q1004.1 (G), Q1005.1 (G), Q1006.1 (G), Q1010.3 (C), Q1011.3 (C), R1050.1
CLMP_BL: D1004.2 (A), D1007.2 (A), D1010.2 (A), D1013.2 (A), D1016.2 (A), D1019.2 (A), D1022.3 (K), R1046.2, U1002.7 (CLAMP)
COM_BH: R1067.2, R1068.1, U1005.1 (K)
COM_BL: C1006.2, C1007.2, C1008.1, C1009.1, C1010.1, C1023.2, D1020.1 (A), D1026.1 (A), Q1012.2 (E), R1006.2, R1011.2, R1017.2, R1023.2, R1029.2, R1035.2, R1041.2, R1054.2, R1059.1, R1074.2, R1075.1, U1002.3 (GND2), U1007.1 (K)
CREF_PHBBH: R1068.2, R1069.1, U1005.2 (REF)
CREF_PHBBL: R1075.2, R1076.1, U1007.2 (REF)
D1_PHB: T1001.1 (D1), U1003.1 (D1)
D2_PHB: T1001.3 (D2), U1003.3 (D2)
DS1_BL: D1028.1 (K), D1029.2 (A)
DTB_BL: R1004.1, U1001.4 (Y)
DTS_BL: C1002.1, D1001.3 (K), R1003.2, U1001.2 (A)
DX_BL: D1024.3 (K), D1026.3 (COM), D1027.3 (K), R1061.1, U1002.2 (DESAT)
DY_BL: D1028.2 (A), R1061.2
EN5: U1002.14 (~RST/EN)
FLT_N: U1002.13 (~FLT)
GND: C1001.2, C1002.2, C1003.2, C1004.2, C1005.2, C1025.2, C1026.2, R1001.2, R1007.2, R1062.2, U1001.3 (GND), U1002.9 (GND1), U1003.4 (GND), U1003.6 (CLK)
G_BL1: C1011.1, D1002.3 (K), D1004.1 (K), Q1001.3 (D), R1008.2, R1009.2, R1010.1, R1013.2
G_BL2: C1013.1, D1005.3 (K), D1007.1 (K), Q1002.3 (D), R1014.2, R1015.2, R1016.1, R1019.2
G_BL3: C1015.1, D1008.3 (K), D1010.1 (K), Q1003.3 (D), R1020.2, R1021.2, R1022.1, R1025.2
G_BL4: C1017.1, D1011.3 (K), D1013.1 (K), Q1004.3 (D), R1026.2, R1027.2, R1028.1, R1031.2
G_BL5: C1019.1, D1014.3 (K), D1016.1 (K), Q1005.3 (D), R1032.2, R1033.2, R1034.1, R1037.2
G_BL6: C1021.1, D1017.3 (K), D1019.1 (K), Q1006.3 (D), R1038.2, R1039.2, R1040.1, R1043.2
INN_BL: C1004.1, R1004.2, U1002.11 (IN-)
INP_BL: C1001.1, R1002.2, U1002.10 (IN+)
KS_BL1: C1011.2, C1012.2, D1003.3 (K), R1010.2, R1011.1
KS_BL2: C1013.2, C1014.2, D1006.3 (K), R1016.2, R1017.1
KS_BL3: C1015.2, C1016.2, D1009.3 (K), R1022.2, R1023.1
KS_BL4: C1017.2, C1018.2, D1012.3 (K), R1028.2, R1029.1
KS_BL5: C1019.2, C1020.2, D1015.3 (K), R1034.2, R1035.1
KS_BL6: C1021.2, C1022.2, D1018.3 (K), R1040.2, R1041.1
NDB_BL: Q1014.1 (B), R1059.2
NDX_BL: D1027.1 (A), Q1014.3 (C), R1060.2
OUTH_BL: D1023.3 (K), R1008.1, R1014.1, R1020.1, R1026.1, R1032.1, R1038.1, R1046.1, U1002.4 (OUTH)
OUTL_BL: Q1008.1 (B), Q1009.1 (B), R1044.1, R1045.1, U1002.6 (OUTL)
P1_BL: R1005.1, R1006.1, U1002.1 (VEE2)
P16_BL: R1007.1, U1002.16 (TEST)
PWM3_5V: D1001.1 (A), R1003.1
PWM4_5V: R1001.1, R1002.1
QIB_BL: Q1010.1 (B), R1048.2, R1049.1
QID_BL: D1021.3 (K), R1049.2
QIZ_BL: D1021.1 (A), D1022.1 (A)
QRB_BL: C1024.2, Q1011.1 (B), R1051.1, R1052.2
QRZ_BL: C1024.1, D1023.1 (A), R1052.1
RAW_PHBBH: C1027.1, D1030.1 (K), D1031.1 (K), Q1015.1 (E), R1063.1
RAW_PHBBL: C1030.1, D1034.1 (K), D1035.1 (K), Q1016.1 (E), R1070.1
RB_PHBBH: Q1015.3 (B), R1063.2, R1064.1
RB_PHBBL: Q1016.3 (B), R1070.2, R1071.1
RDY: U1002.12 (RDY)
RK_PHBBH: C1028.1, R1064.2, U1004.1 (K)
RK_PHBBL: C1031.1, R1071.2, U1006.1 (K)
RREF_PHBBH: C1028.2, R1065.2, R1066.1, U1004.2 (REF)
RREF_PHBBL: C1031.2, R1072.2, R1073.1, U1006.2 (REF)
SA_PHBBH: D1030.2 (A), D1032.1 (K), T1001.4 (S1A)
SA_PHBBL: D1034.2 (A), D1036.1 (K), T1001.6 (S2A)
SB_BL: Q1007.3 (D), R1013.1, R1019.1, R1025.1, R1031.1, R1037.1, R1043.1
SB_PHBBH: D1031.2 (A), D1033.1 (K), T1001.5 (S1B)
SB_PHBBL: D1035.2 (A), D1037.1 (K), T1001.7 (S2B)
SK1_BL: Q1008.2 (E), R1009.1, R1015.1, R1021.1, R1044.2
SK2_BL: Q1009.2 (E), R1027.1, R1033.1, R1039.1, R1045.2
SW_B: D1029.1 (K)
VCG_BL: C1023.1, D1020.3 (K), Q1010.2 (E), R1047.2, R1048.1
VDD_BH: C1029.1, Q1015.2 (C), R1065.1, R1067.1
VDD_BL: C1006.1, C1007.1, C1032.1, D1026.2 (K), Q1013.2 (E), Q1016.2 (C), R1047.1, R1056.2, R1060.1, R1072.1, R1074.1, U1002.5 (VCC2)
VEEL1_BL: C1012.1, Q1001.2 (S), R1012.2
VEEL2_BL: C1014.1, Q1002.2 (S), R1018.2
VEEL3_BL: C1016.1, Q1003.2 (S), R1024.2
VEEL4_BL: C1018.1, Q1004.2 (S), R1030.2
VEEL5_BL: C1020.1, Q1005.2 (S), R1036.2
VEEL6_BL: C1022.1, Q1006.2 (S), R1042.2
VEE_BH: C1027.2, C1029.2, D1032.2 (A), D1033.2 (A), R1066.2, R1069.2, U1004.3 (A), U1005.3 (A)
VEE_BL: C1008.2, C1009.2, C1010.2, C1030.2, C1032.2, D1025.1 (A), D1036.2 (A), D1037.2 (A), Q1007.2 (S), Q1008.3 (C), Q1009.3 (C), Q1011.2 (E), Q1014.2 (E), R1005.2, R1012.1, R1018.1, R1024.1, R1030.1, R1036.1, R1042.1, R1050.2, R1051.2, R1058.2, R1073.2, R1076.2, U1002.8 (VEE2), U1006.3 (A), U1007.3 (A)
ZM1_BL: D1002.1 (A), D1003.1 (A)
ZM2_BL: D1005.1 (A), D1006.1 (A)
ZM3_BL: D1008.1 (A), D1009.1 (A)
ZM4_BL: D1011.1 (A), D1012.1 (A)
ZM5_BL: D1014.1 (A), D1015.1 (A)
ZM6_BL: D1017.1 (A), D1018.1 (A)

Notes on the sheet:
Gate and Kelvin of each device as coupled pairs of equal length from the COM star; Ron, Roff, Kelvin R, 10k + 1n, Zeners and the clamp FET + C_VL at each device (loop <= 1 nH). PNP followers next to their three gates. DESAT string >= 2.5 mm pad gap per diode; coat to PD1. Miller hold of six gates N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
BL: LOGIC SIDE
LEG B: LAYOUT RULES
DESAT pin (internal 500 uA blanking source, trip 8.5-10.0 V) - Rs - 2 x BYG23T-M3/TR (1300 V each) - drain. BAT54S keeps DX between COM and VDD against dv/dt through the string; Cblk footprint DNP.
BL: MILLER CLAMP CONTROL
PHB: GATE BIAS (PER PHASE)
BL: TURN-OFF BUFFER
BL: DESAT
MMBT3906 inverter (E COM, base BAT54+2.2k on CLAMP) drives CG to COM once the lowest gate is below ~-1.2 V; MMBT3904 release (from OUTH via 5.6 V Zener) holds CG at VEE while OUTH drives.
BL: DRIVER AND 6 GATES
SN6505B push-pull 420 kHz from +5V_GD, BIAS_EN high = on; T_BIAS4 custom, functional insulation (PD-free >= 1.75 kVpk, <= 5 pF per secondary). Per channel: bridge, PNP regulator VDD-VEE, ATL431 COM split.
DESAT > 10.3-10.9 V (above the 10.0 V maximum trip of the -Q1 grade) -> MMBT3904 -> MMBT3906 charges BG to VEE + 10 V; per device AO3400A + 22R pull the gate to VEE; BG holds ~3 us (1k + FET gates).
BL: SHORT-CIRCUIT BOOSTER
IN+ = own PWM; IN- = complementary switch, falling edge stretched 3.65k/100p (interlock + min dead time = max(firmware, hardware)). Bias PG (active low) pulls RDY low.
Per device: Ron/Roff, 0.5R Kelvin R to the COM star, 10k and Zeners (about +21 V / -5.7 V) on its own Kelvin net. Miller hold: N-MOSFET clamp (PMV30ENEA) gate-pin to a local VEE (1u on the Kelvin pin). LAYOUT: FET + 1u at the device, loop <= 1 nH.
2 x ZXTP25040DFH emitter followers on OUTL (B-E 1k, C to VEE): each sinks the Roff current of 3 gates; the NSI6651 supplies base current only. Turn-on stays on OUTH.
