vectivolt/PCM/hardware/PCS-PWR-4W/sheets/12_gdcl.kicad_sch

## KiCad design hardware/PCS-PWR-4W/sheets/12_gdcl.kicad_sch (2026-10-07)

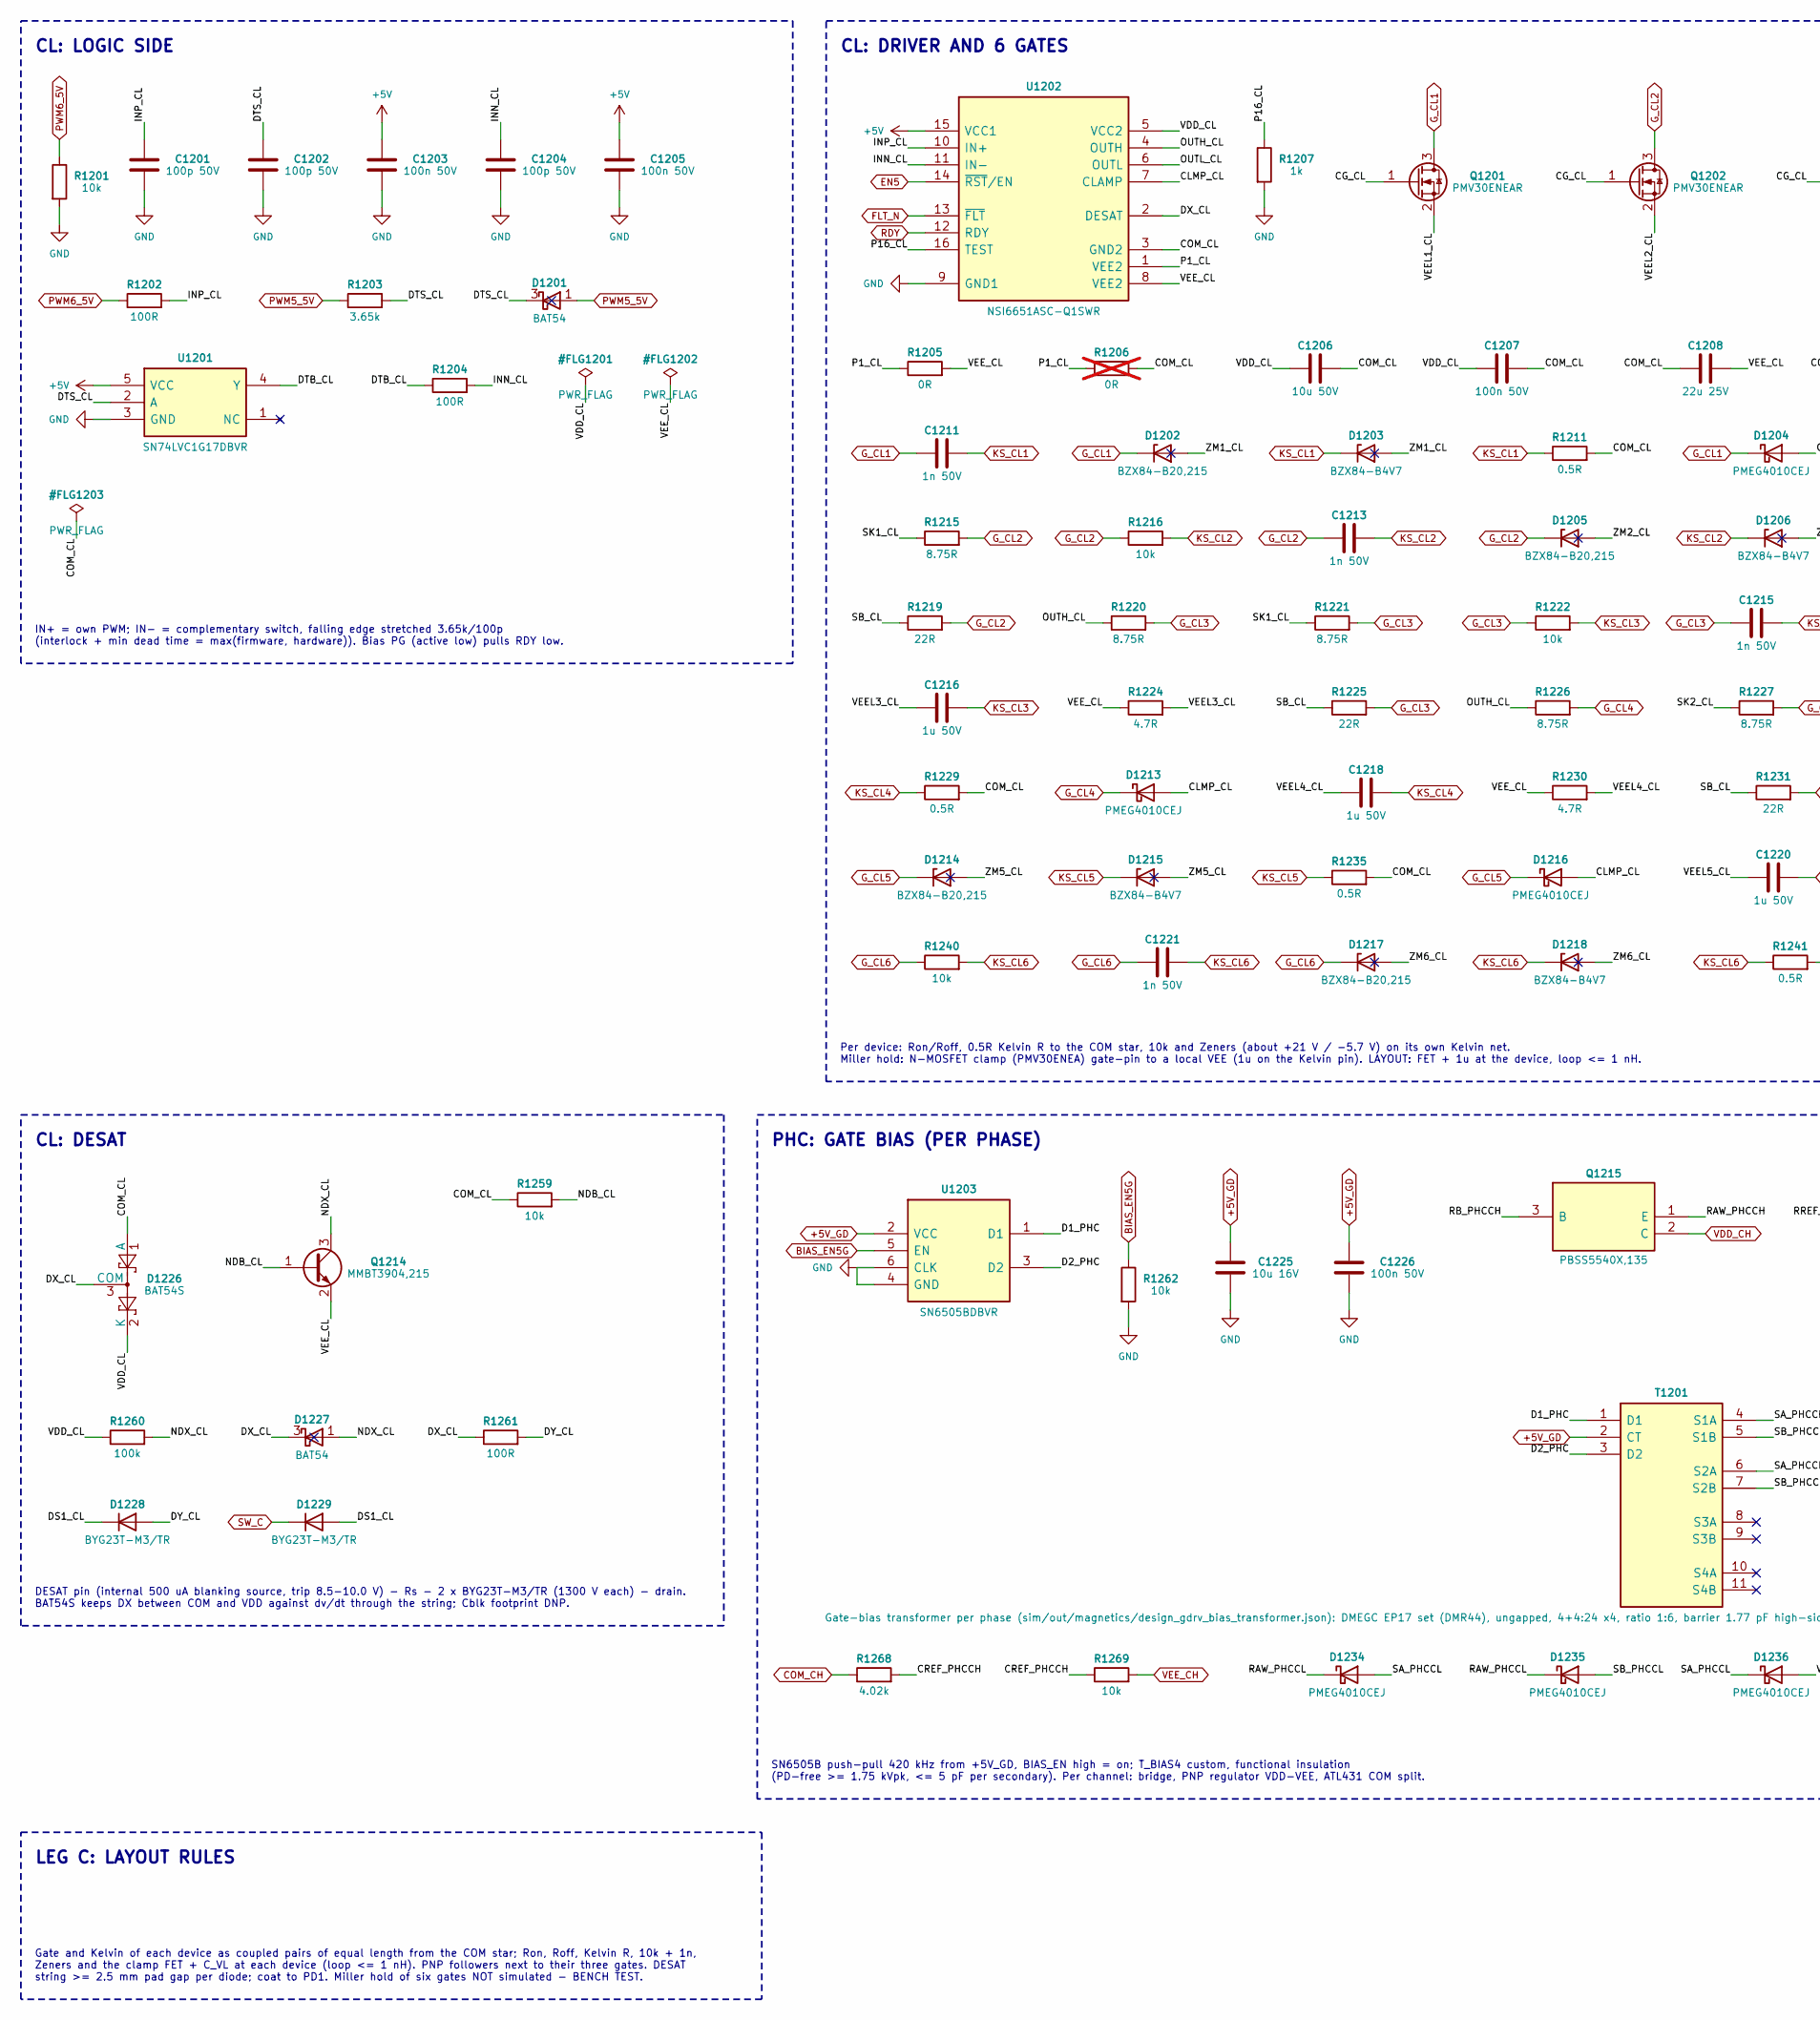
[picture p319: schematic 12_gdcl.kicad_sch, part in row 1, column 1]

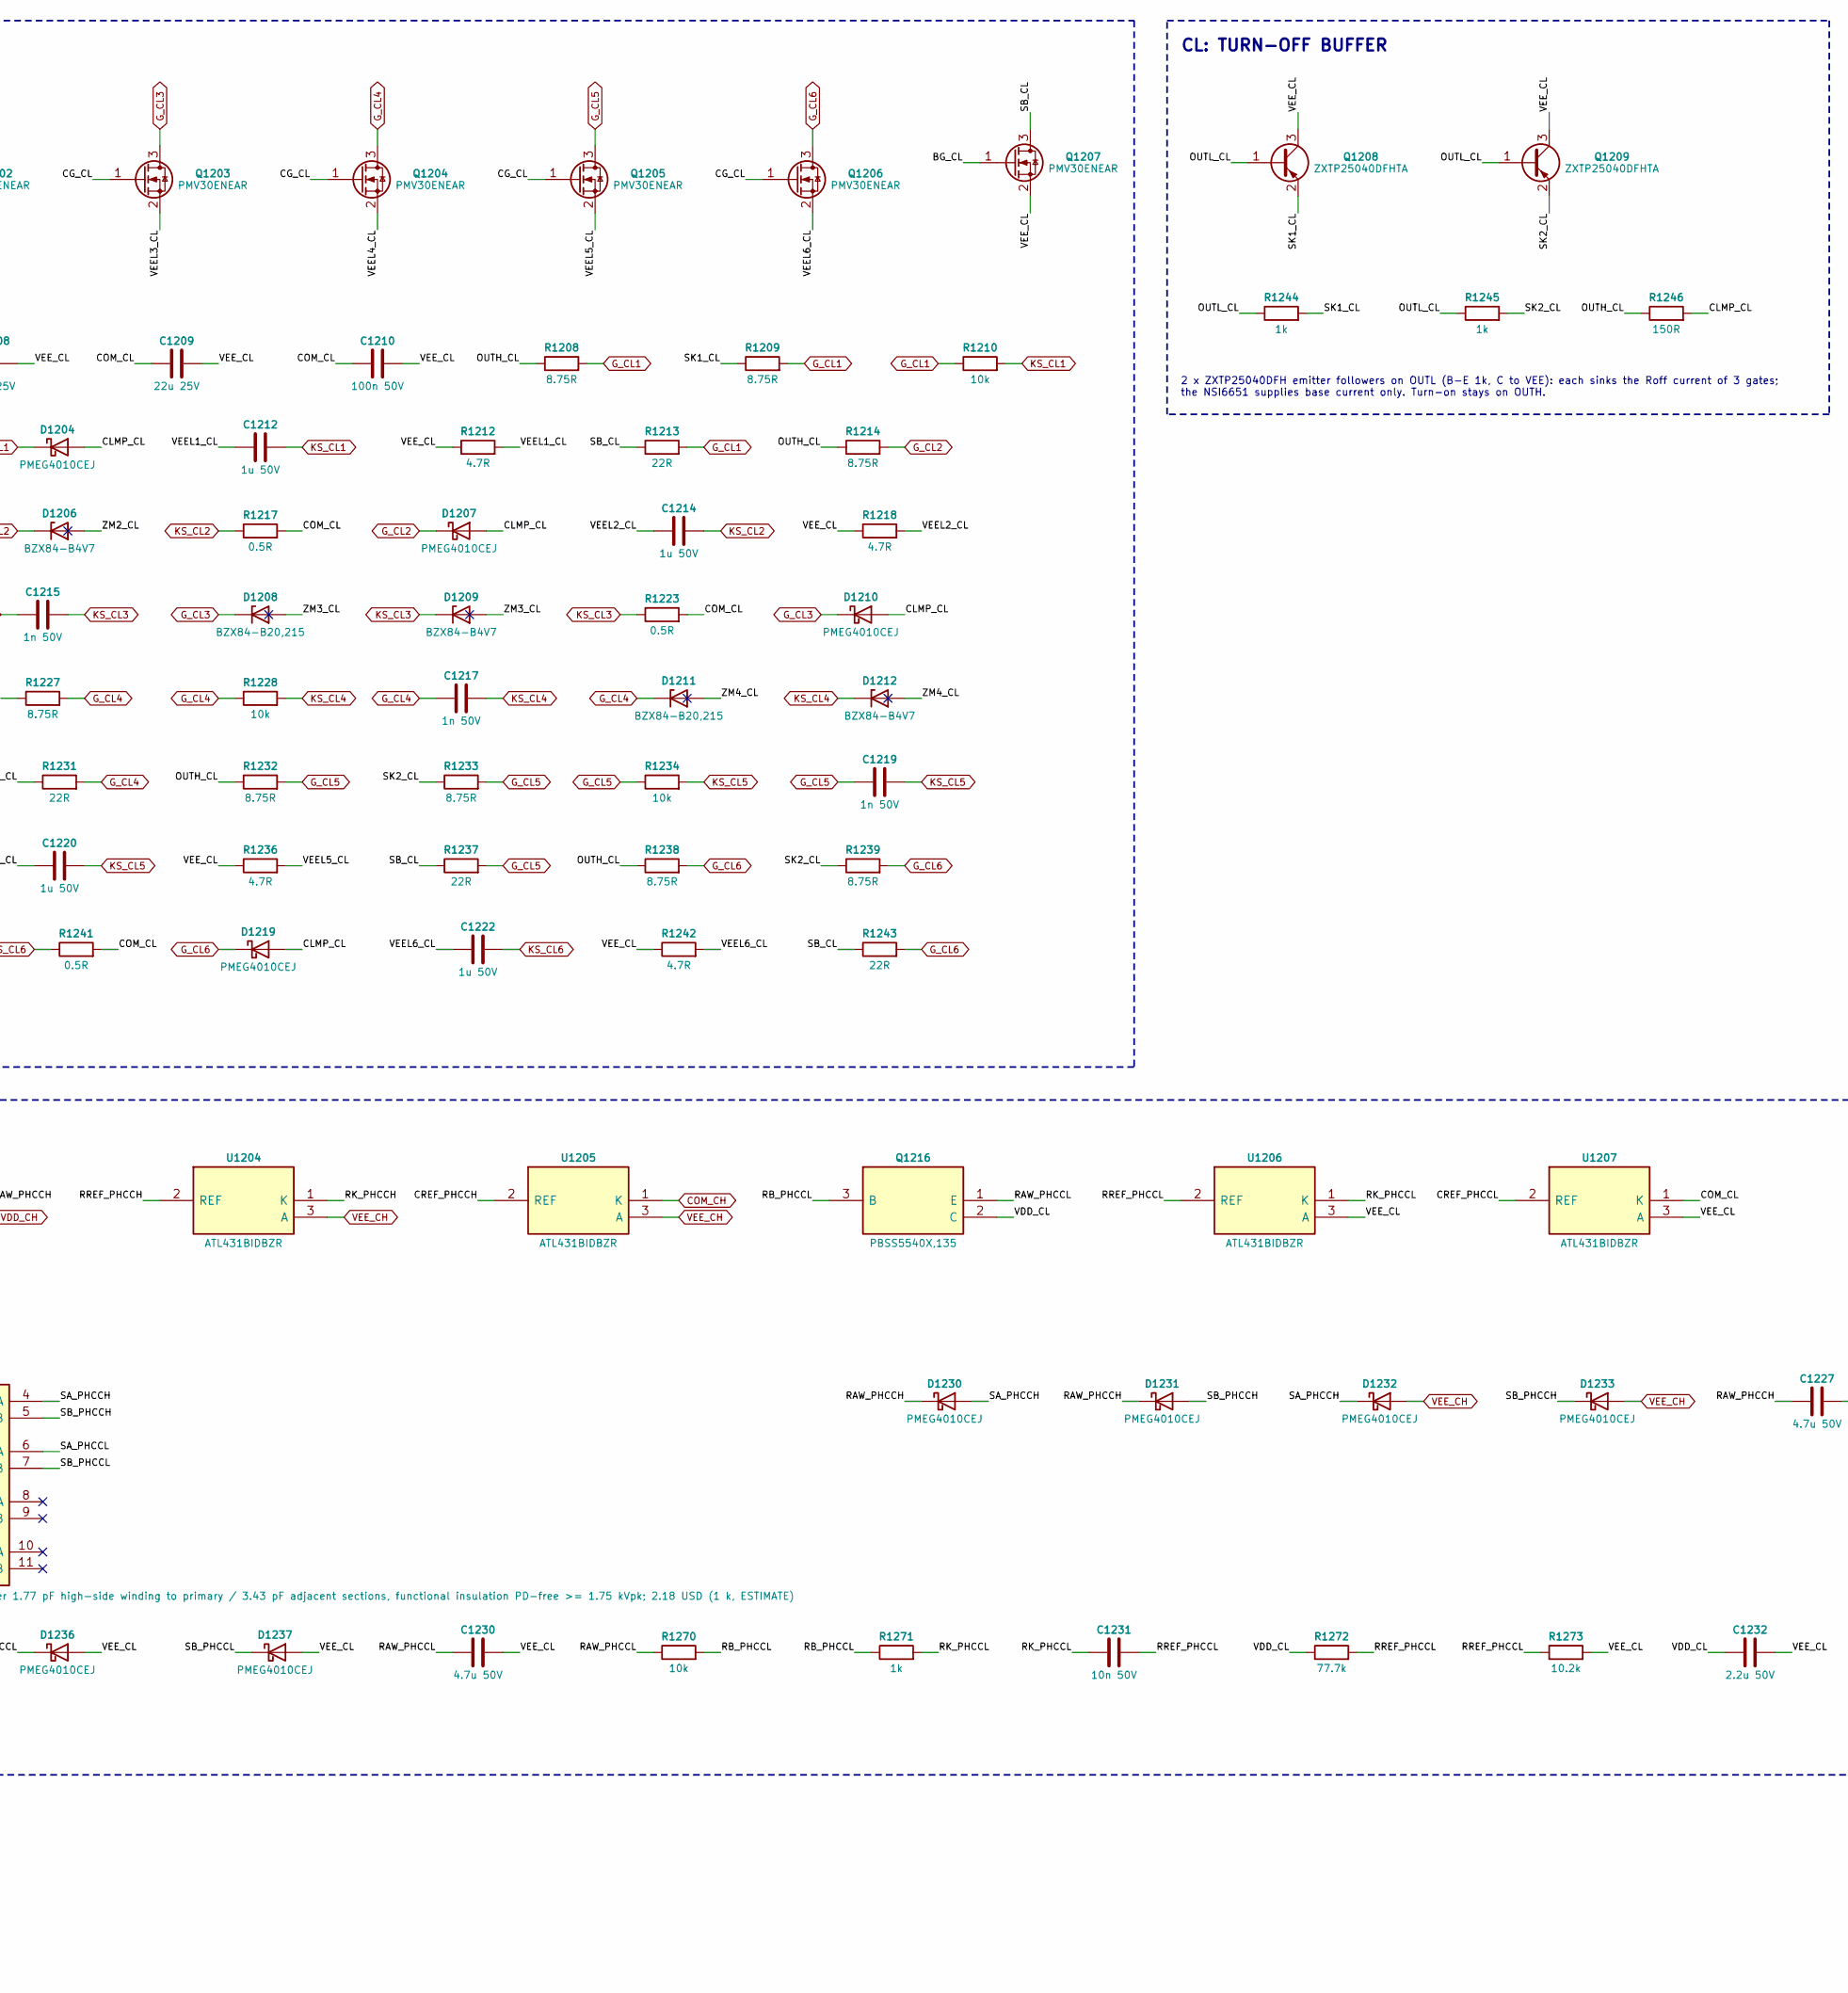
[picture p320: schematic 12_gdcl.kicad_sch, part in row 1, column 2]

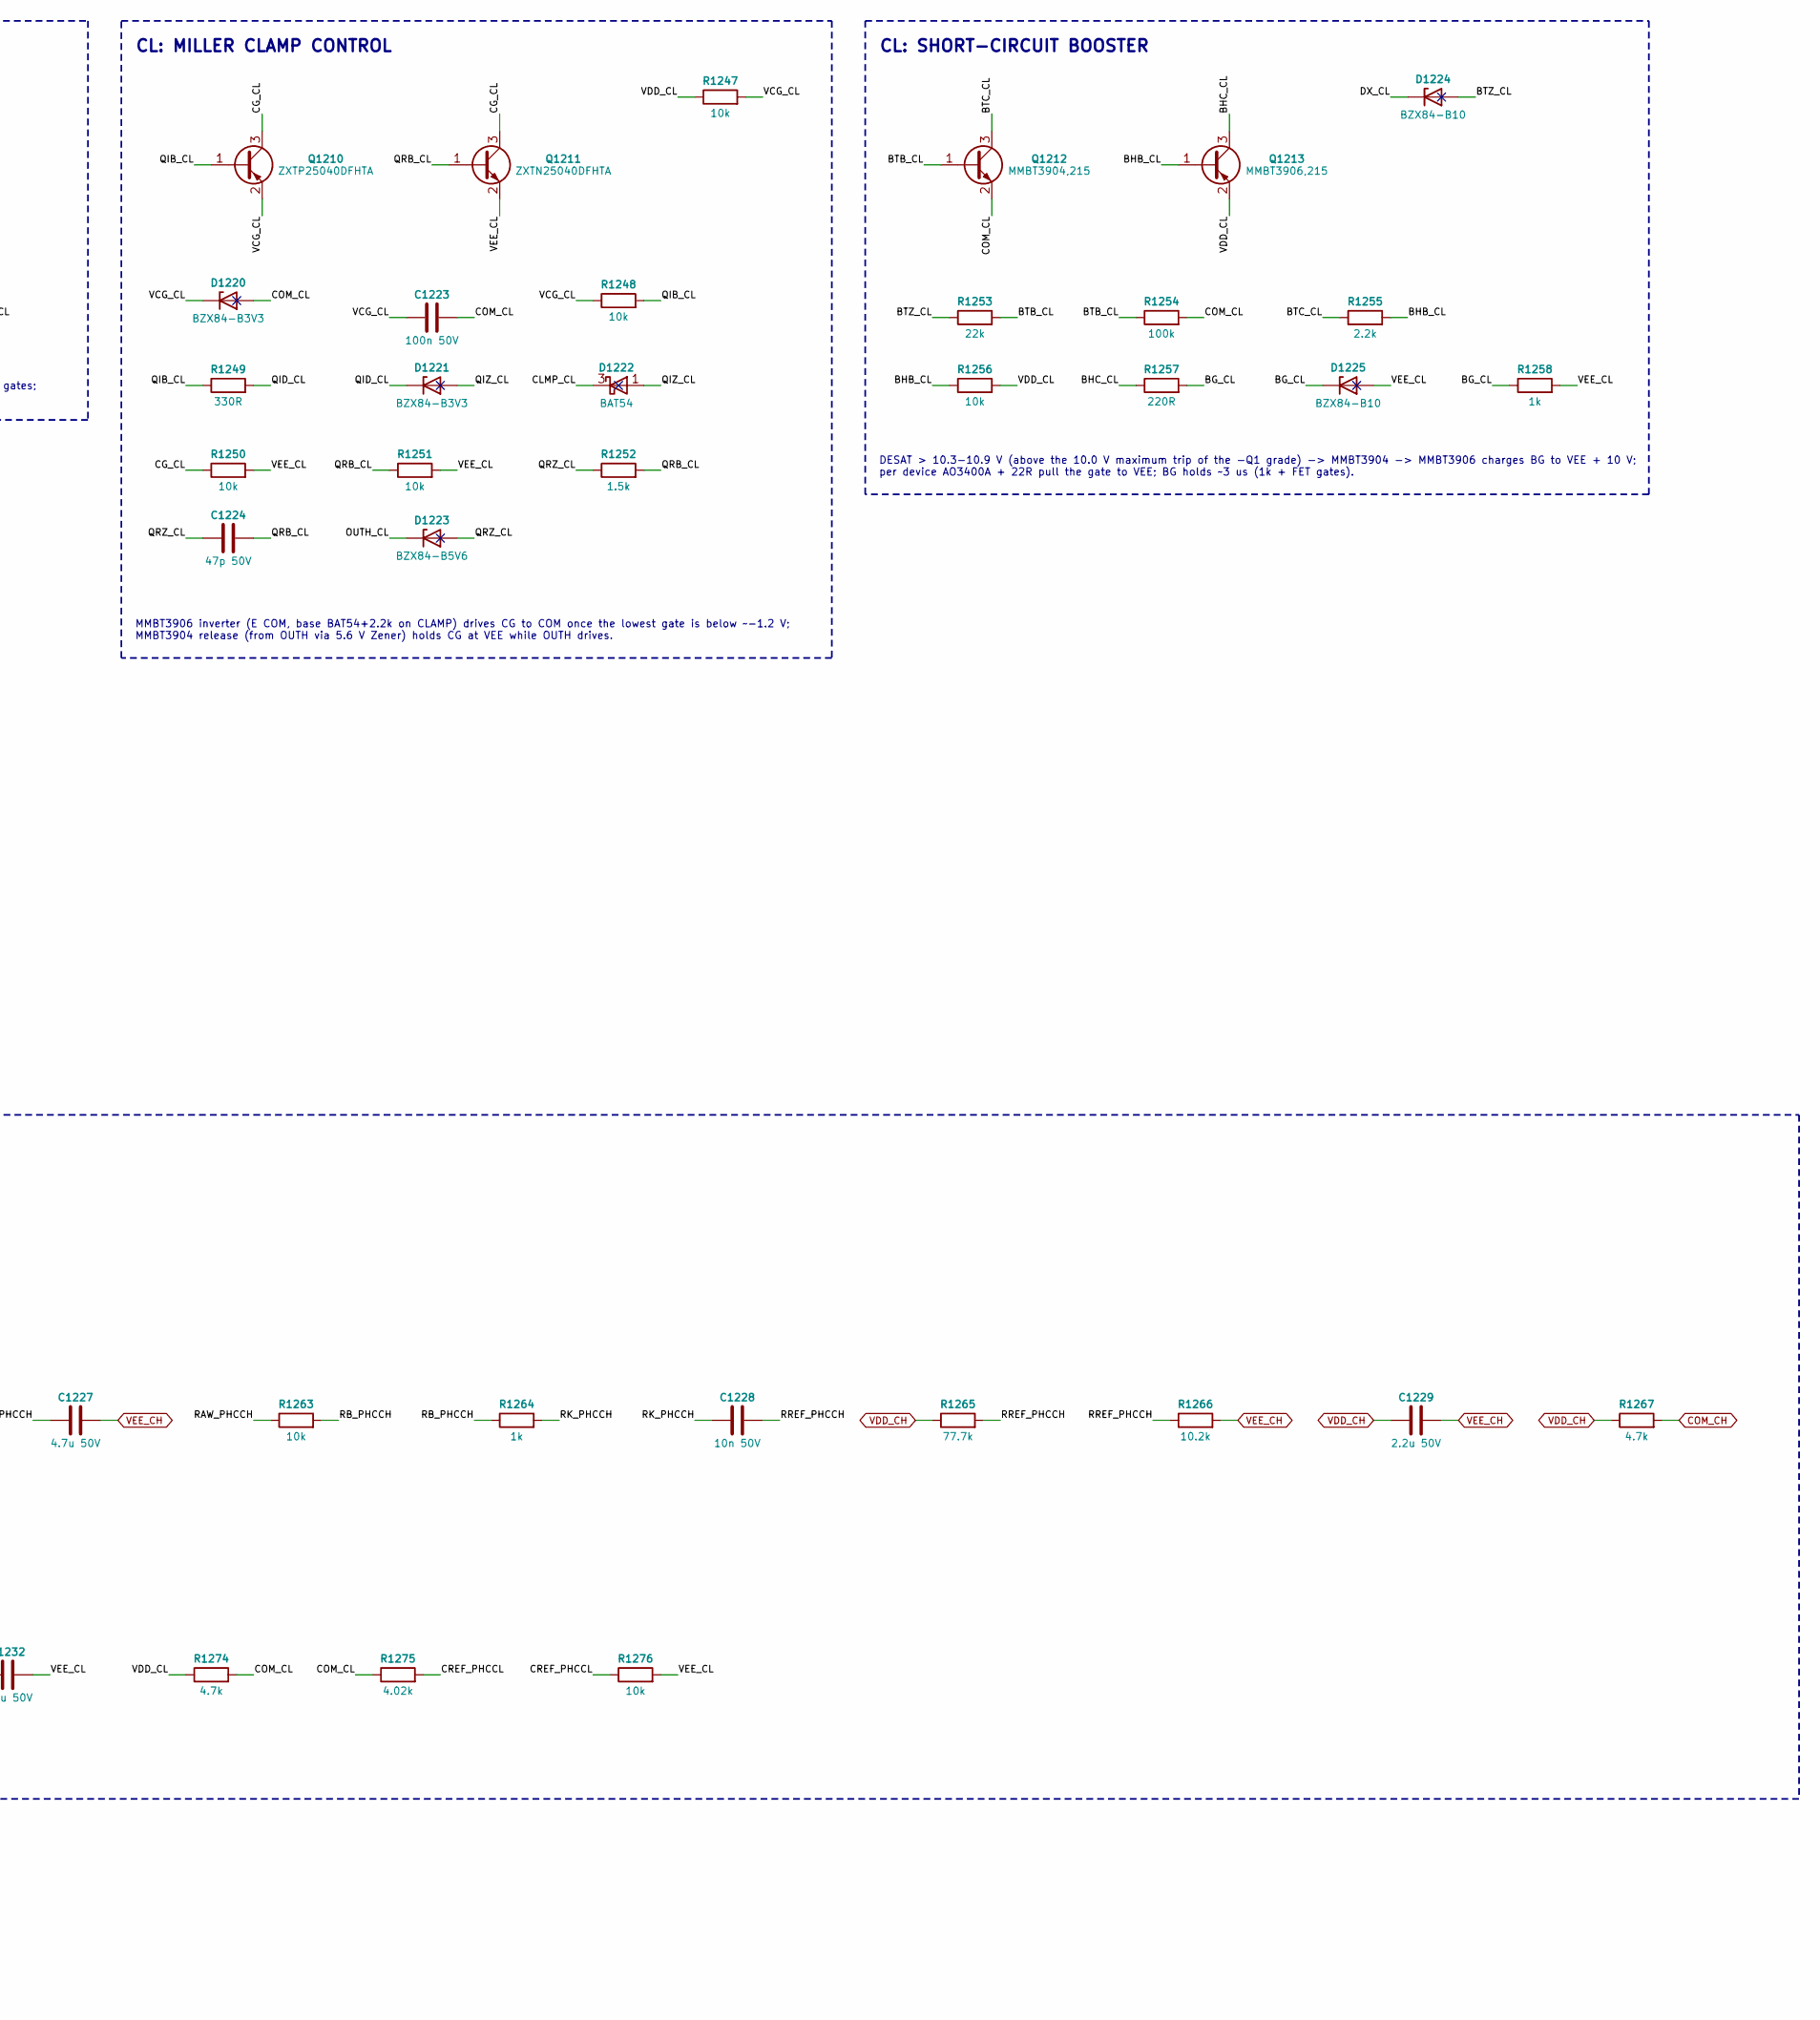
[picture p321: schematic 12_gdcl.kicad_sch, part in row 1, column 3]

Parts:
C1201, C1202, C1204: 100p 50V
C1203, C1205, C1207, C1210, C1223, C1226: 100n 50V
C1206: 10u 50V
C1208, C1209: 22u 25V
C1211, C1213, C1215, C1217, C1219, C1221: 1n 50V
C1212, C1214, C1216, C1218, C1220, C1222: 1u 50V
C1224: 47p 50V
C1225: 10u 16V
C1227, C1230: 4.7u 50V
C1228, C1231: 10n 50V
C1229, C1232: 2.2u 50V
D1201, D1222, D1227: BAT54; MPN BAT54
D1202, D1205, D1208, D1211, D1214, D1217: BZX84-B20,215; MPN BZX84-B20,215
D1203, D1206, D1209, D1212, D1215, D1218: BZX84-B4V7; MPN BZX84-B4V7
D1204, D1207, D1210, D1213, D1216, D1219, D1230, D1231, D1232, D1233, D1234, D1235, D1236, D1237: PMEG4010CEJ; MPN PMEG4010CEJ
D1220, D1221: BZX84-B3V3; MPN BZX84-B3V3
D1223: BZX84-B5V6; MPN BZX84-B5V6
D1224, D1225: BZX84-B10; MPN BZX84-B10
D1226: BAT54S; MPN BAT54S
D1228, D1229: BYG23T-M3/TR; MPN BYG23T-M3/TR
Q1201, Q1202, Q1203, Q1204, Q1205, Q1206, Q1207: PMV30ENEAR; MPN PMV30ENEAR
Q1208, Q1209, Q1210: ZXTP25040DFHTA; MPN ZXTP25040DFHTA
Q1211: ZXTN25040DFHTA; MPN ZXTN25040DFHTA
Q1212, Q1214: MMBT3904,215; MPN MMBT3904,215
Q1213: MMBT3906,215; MPN MMBT3906,215
Q1215, Q1216: PBSS5540X,135; MPN PBSS5540X,135
R1201, R1210, R1216, R1222, R1228, R1234, R1240, R1247, R1248, R1250, R1251, R1256, R1259, R1262, R1263, R1269, R1270, R1276: 10k
R1202, R1204, R1261: 100R
R1203: 3.65k
R1205: 0R
R1206: 0R; not fitted
R1207, R1244, R1245, R1258, R1264, R1271: 1k
R1208, R1209, R1214, R1215, R1220, R1221, R1226, R1227, R1232, R1233, R1238, R1239: 8.75R
R1211, R1217, R1223, R1229, R1235, R1241: 0.5R
R1212, R1218, R1224, R1230, R1236, R1242: 4.7R
R1213, R1219, R1225, R1231, R1237, R1243: 22R
R1246: 150R
R1249: 330R
R1252: 1.5k
R1253: 22k
R1254, R1260: 100k
R1255: 2.2k
R1257: 220R
R1265, R1272: 77.7k
R1266, R1273: 10.2k
R1267, R1274: 4.7k
R1268, R1275: 4.02k
T1201: Gate-bias transformer per phase (sim/out/magnetic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
U1201: SN74LVC1G17DBVR; MPN SN74LVC1G17DBVR
U1202: NSI6651ASC-Q1SWR; MPN NSI6651ASC-Q1SWR
U1203: SN6505BDBVR; MPN SN6505BDBVR
U1204, U1205, U1206, U1207: ATL431BIDBZR; MPN ATL431BIDBZR

Connections:
+5V: C1203.1, C1205.1, U1201.5 (VCC), U1202.15 (VCC1)
+5V_GD: C1225.1, C1226.1, T1201.2 (CT), U1203.2 (VCC)
BG_CL: D1225.3 (K), Q1207.1 (G), R1257.2, R1258.1
BHB_CL: Q1213.1 (B), R1255.2, R1256.1
BHC_CL: Q1213.3 (C), R1257.1
BIAS_EN5G: R1262.1, U1203.5 (EN)
BTB_CL: Q1212.1 (B), R1253.2, R1254.1
BTC_CL: Q1212.3 (C), R1255.1
BTZ_CL: D1224.1 (A), R1253.1
CG_CL: Q1201.1 (G), Q1202.1 (G), Q1203.1 (G), Q1204.1 (G), Q1205.1 (G), Q1206.1 (G), Q1210.3 (C), Q1211.3 (C), R1250.1
CLMP_CL: D1204.2 (A), D1207.2 (A), D1210.2 (A), D1213.2 (A), D1216.2 (A), D1219.2 (A), D1222.3 (K), R1246.2, U1202.7 (CLAMP)
COM_CH: R1267.2, R1268.1, U1205.1 (K)
COM_CL: C1206.2, C1207.2, C1208.1, C1209.1, C1210.1, C1223.2, D1220.1 (A), D1226.1 (A), Q1212.2 (E), R1206.2, R1211.2, R1217.2, R1223.2, R1229.2, R1235.2, R1241.2, R1254.2, R1259.1, R1274.2, R1275.1, U1202.3 (GND2), U1207.1 (K)
CREF_PHCCH: R1268.2, R1269.1, U1205.2 (REF)
CREF_PHCCL: R1275.2, R1276.1, U1207.2 (REF)
D1_PHC: T1201.1 (D1), U1203.1 (D1)
D2_PHC: T1201.3 (D2), U1203.3 (D2)
DS1_CL: D1228.1 (K), D1229.2 (A)
DTB_CL: R1204.1, U1201.4 (Y)
DTS_CL: C1202.1, D1201.3 (K), R1203.2, U1201.2 (A)
DX_CL: D1224.3 (K), D1226.3 (COM), D1227.3 (K), R1261.1, U1202.2 (DESAT)
DY_CL: D1228.2 (A), R1261.2
EN5: U1202.14 (~RST/EN)
FLT_N: U1202.13 (~FLT)
GND: C1201.2, C1202.2, C1203.2, C1204.2, C1205.2, C1225.2, C1226.2, R1201.2, R1207.2, R1262.2, U1201.3 (GND), U1202.9 (GND1), U1203.4 (GND), U1203.6 (CLK)
G_CL1: C1211.1, D1202.3 (K), D1204.1 (K), Q1201.3 (D), R1208.2, R1209.2, R1210.1, R1213.2
G_CL2: C1213.1, D1205.3 (K), D1207.1 (K), Q1202.3 (D), R1214.2, R1215.2, R1216.1, R1219.2
G_CL3: C1215.1, D1208.3 (K), D1210.1 (K), Q1203.3 (D), R1220.2, R1221.2, R1222.1, R1225.2
G_CL4: C1217.1, D1211.3 (K), D1213.1 (K), Q1204.3 (D), R1226.2, R1227.2, R1228.1, R1231.2
G_CL5: C1219.1, D1214.3 (K), D1216.1 (K), Q1205.3 (D), R1232.2, R1233.2, R1234.1, R1237.2
G_CL6: C1221.1, D1217.3 (K), D1219.1 (K), Q1206.3 (D), R1238.2, R1239.2, R1240.1, R1243.2
INN_CL: C1204.1, R1204.2, U1202.11 (IN-)
INP_CL: C1201.1, R1202.2, U1202.10 (IN+)
KS_CL1: C1211.2, C1212.2, D1203.3 (K), R1210.2, R1211.1
KS_CL2: C1213.2, C1214.2, D1206.3 (K), R1216.2, R1217.1
KS_CL3: C1215.2, C1216.2, D1209.3 (K), R1222.2, R1223.1
KS_CL4: C1217.2, C1218.2, D1212.3 (K), R1228.2, R1229.1
KS_CL5: C1219.2, C1220.2, D1215.3 (K), R1234.2, R1235.1
KS_CL6: C1221.2, C1222.2, D1218.3 (K), R1240.2, R1241.1
NDB_CL: Q1214.1 (B), R1259.2
NDX_CL: D1227.1 (A), Q1214.3 (C), R1260.2
OUTH_CL: D1223.3 (K), R1208.1, R1214.1, R1220.1, R1226.1, R1232.1, R1238.1, R1246.1, U1202.4 (OUTH)
OUTL_CL: Q1208.1 (B), Q1209.1 (B), R1244.1, R1245.1, U1202.6 (OUTL)
P1_CL: R1205.1, R1206.1, U1202.1 (VEE2)
P16_CL: R1207.1, U1202.16 (TEST)
PWM5_5V: D1201.1 (A), R1203.1
PWM6_5V: R1201.1, R1202.1
QIB_CL: Q1210.1 (B), R1248.2, R1249.1
QID_CL: D1221.3 (K), R1249.2
QIZ_CL: D1221.1 (A), D1222.1 (A)
QRB_CL: C1224.2, Q1211.1 (B), R1251.1, R1252.2
QRZ_CL: C1224.1, D1223.1 (A), R1252.1
RAW_PHCCH: C1227.1, D1230.1 (K), D1231.1 (K), Q1215.1 (E), R1263.1
RAW_PHCCL: C1230.1, D1234.1 (K), D1235.1 (K), Q1216.1 (E), R1270.1
RB_PHCCH: Q1215.3 (B), R1263.2, R1264.1
RB_PHCCL: Q1216.3 (B), R1270.2, R1271.1
RDY: U1202.12 (RDY)
RK_PHCCH: C1228.1, R1264.2, U1204.1 (K)
RK_PHCCL: C1231.1, R1271.2, U1206.1 (K)
RREF_PHCCH: C1228.2, R1265.2, R1266.1, U1204.2 (REF)
RREF_PHCCL: C1231.2, R1272.2, R1273.1, U1206.2 (REF)
SA_PHCCH: D1230.2 (A), D1232.1 (K), T1201.4 (S1A)
SA_PHCCL: D1234.2 (A), D1236.1 (K), T1201.6 (S2A)
SB_CL: Q1207.3 (D), R1213.1, R1219.1, R1225.1, R1231.1, R1237.1, R1243.1
SB_PHCCH: D1231.2 (A), D1233.1 (K), T1201.5 (S1B)
SB_PHCCL: D1235.2 (A), D1237.1 (K), T1201.7 (S2B)
SK1_CL: Q1208.2 (E), R1209.1, R1215.1, R1221.1, R1244.2
SK2_CL: Q1209.2 (E), R1227.1, R1233.1, R1239.1, R1245.2
SW_C: D1229.1 (K)
VCG_CL: C1223.1, D1220.3 (K), Q1210.2 (E), R1247.2, R1248.1
VDD_CH: C1229.1, Q1215.2 (C), R1265.1, R1267.1
VDD_CL: C1206.1, C1207.1, C1232.1, D1226.2 (K), Q1213.2 (E), Q1216.2 (C), R1247.1, R1256.2, R1260.1, R1272.1, R1274.1, U1202.5 (VCC2)
VEEL1_CL: C1212.1, Q1201.2 (S), R1212.2
VEEL2_CL: C1214.1, Q1202.2 (S), R1218.2
VEEL3_CL: C1216.1, Q1203.2 (S), R1224.2
VEEL4_CL: C1218.1, Q1204.2 (S), R1230.2
VEEL5_CL: C1220.1, Q1205.2 (S), R1236.2
VEEL6_CL: C1222.1, Q1206.2 (S), R1242.2
VEE_CH: C1227.2, C1229.2, D1232.2 (A), D1233.2 (A), R1266.2, R1269.2, U1204.3 (A), U1205.3 (A)
VEE_CL: C1208.2, C1209.2, C1210.2, C1230.2, C1232.2, D1225.1 (A), D1236.2 (A), D1237.2 (A), Q1207.2 (S), Q1208.3 (C), Q1209.3 (C), Q1211.2 (E), Q1214.2 (E), R1205.2, R1212.1, R1218.1, R1224.1, R1230.1, R1236.1, R1242.1, R1250.2, R1251.2, R1258.2, R1273.2, R1276.2, U1202.8 (VEE2), U1206.3 (A), U1207.3 (A)
ZM1_CL: D1202.1 (A), D1203.1 (A)
ZM2_CL: D1205.1 (A), D1206.1 (A)
ZM3_CL: D1208.1 (A), D1209.1 (A)
ZM4_CL: D1211.1 (A), D1212.1 (A)
ZM5_CL: D1214.1 (A), D1215.1 (A)
ZM6_CL: D1217.1 (A), D1218.1 (A)

Notes on the sheet:
MMBT3906 inverter (E COM, base BAT54+2.2k on CLAMP) drives CG to COM once the lowest gate is below ~-1.2 V; MMBT3904 release (from OUTH via 5.6 V Zener) holds CG at VEE while OUTH drives.
CL: DESAT
CL: DRIVER AND 6 GATES
2 x ZXTP25040DFH emitter followers on OUTL (B-E 1k, C to VEE): each sinks the Roff current of 3 gates; the NSI6651 supplies base current only. Turn-on stays on OUTH.
SN6505B push-pull 420 kHz from +5V_GD, BIAS_EN high = on; T_BIAS4 custom, functional insulation (PD-free >= 1.75 kVpk, <= 5 pF per secondary). Per channel: bridge, PNP regulator VDD-VEE, ATL431 COM split.
CL: LOGIC SIDE
CL: MILLER CLAMP CONTROL
IN+ = own PWM; IN- = complementary switch, falling edge stretched 3.65k/100p (interlock + min dead time = max(firmware, hardware)). Bias PG (active low) pulls RDY low.
DESAT pin (internal 500 uA blanking source, trip 8.5-10.0 V) - Rs - 2 x BYG23T-M3/TR (1300 V each) - drain. BAT54S keeps DX between COM and VDD against dv/dt through the string; Cblk footprint DNP.
Per device: Ron/Roff, 0.5R Kelvin R to the COM star, 10k and Zeners (about +21 V / -5.7 V) on its own Kelvin net. Miller hold: N-MOSFET clamp (PMV30ENEA) gate-pin to a local VEE (1u on the Kelvin pin). LAYOUT: FET + 1u at the device, loop <= 1 nH.
CL: TURN-OFF BUFFER
PHC: GATE BIAS (PER PHASE)
Gate and Kelvin of each device as coupled pairs of equal length from the COM star; Ron, Roff, Kelvin R, 10k + 1n, Zeners and the clamp FET + C_VL at each device (loop <= 1 nH). PNP followers next to their three gates. DESAT string >= 2.5 mm pad gap per diode; coat to PD1. Miller hold of six gates N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
CL: SHORT-CIRCUIT BOOSTER
DESAT > 10.3-10.9 V (above the 10.0 V maximum trip of the -Q1 grade) -> MMBT3904 -> MMBT3906 charges BG to VEE + 10 V; per device AO3400A + 22R pull the gate to VEE; BG holds ~3 us (1k + FET gates).
LEG C: LAYOUT RULES
