vectivolt/PCM/hardware/PCS-PWR-4W/sheets/13_gdnh.kicad_sch

## KiCad design hardware/PCS-PWR-4W/sheets/13_gdnh.kicad_sch (2026-10-07)

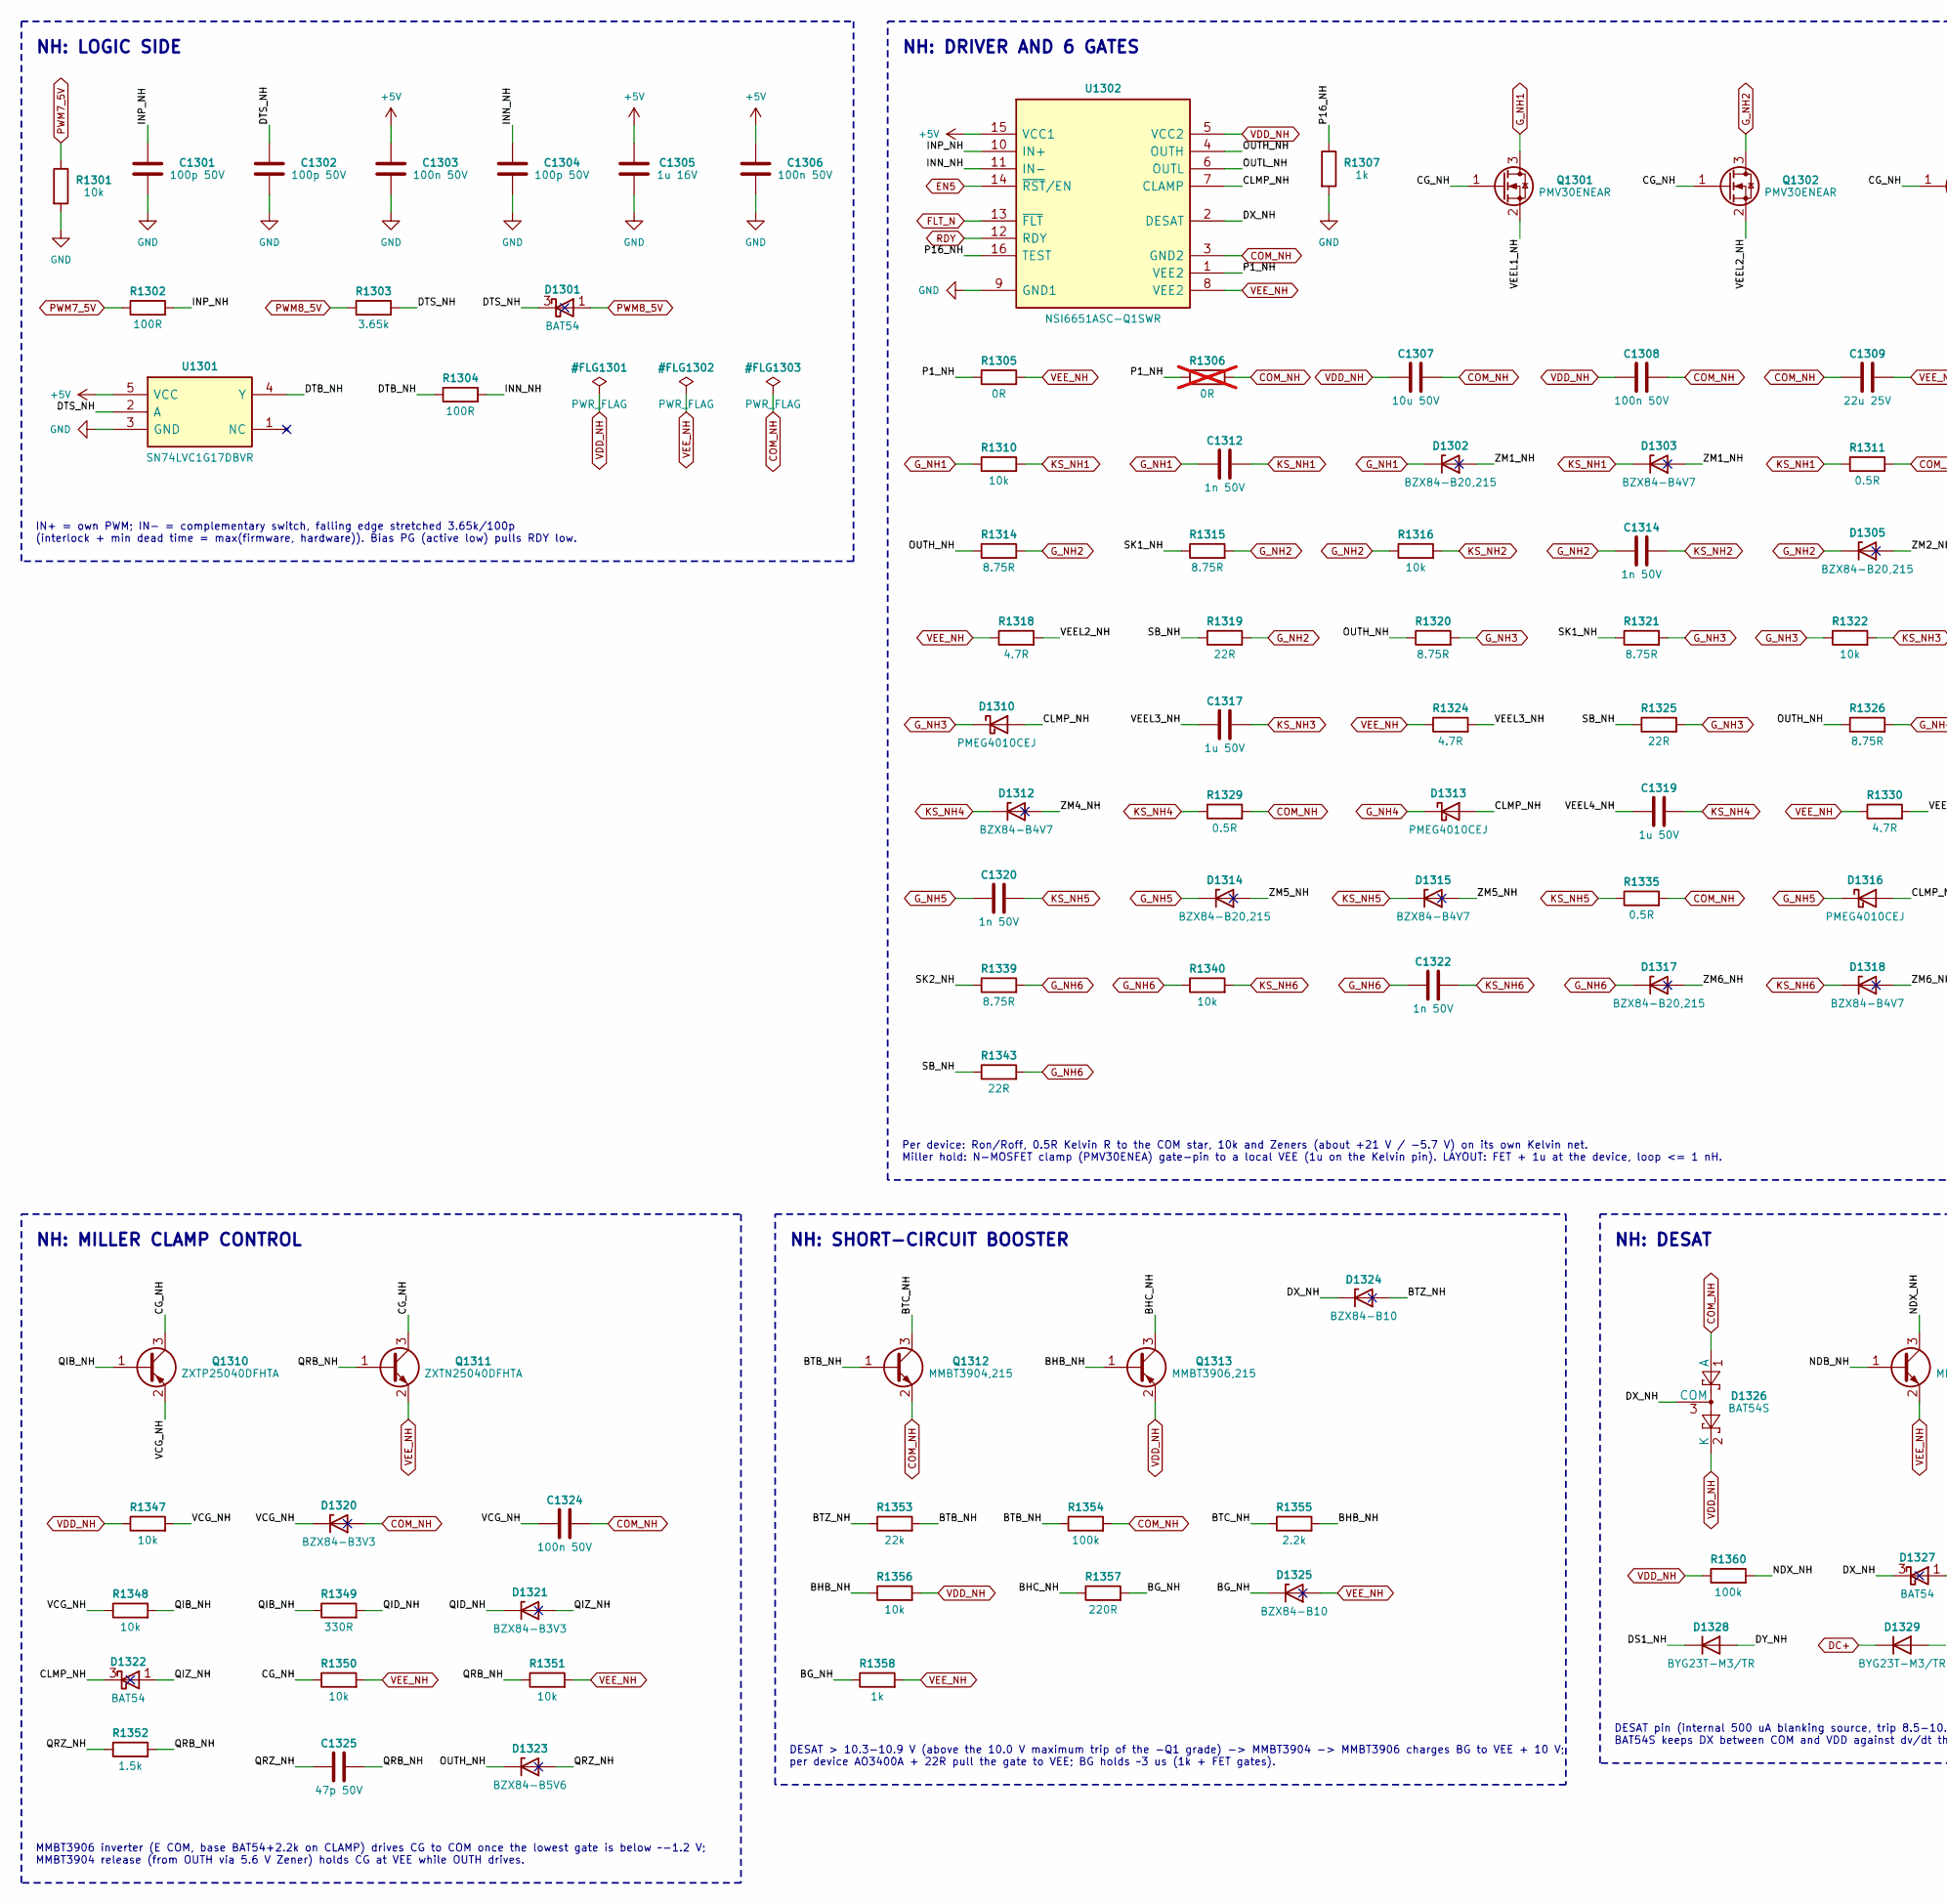
[picture p322: schematic 13_gdnh.kicad_sch, part in row 1, column 1]

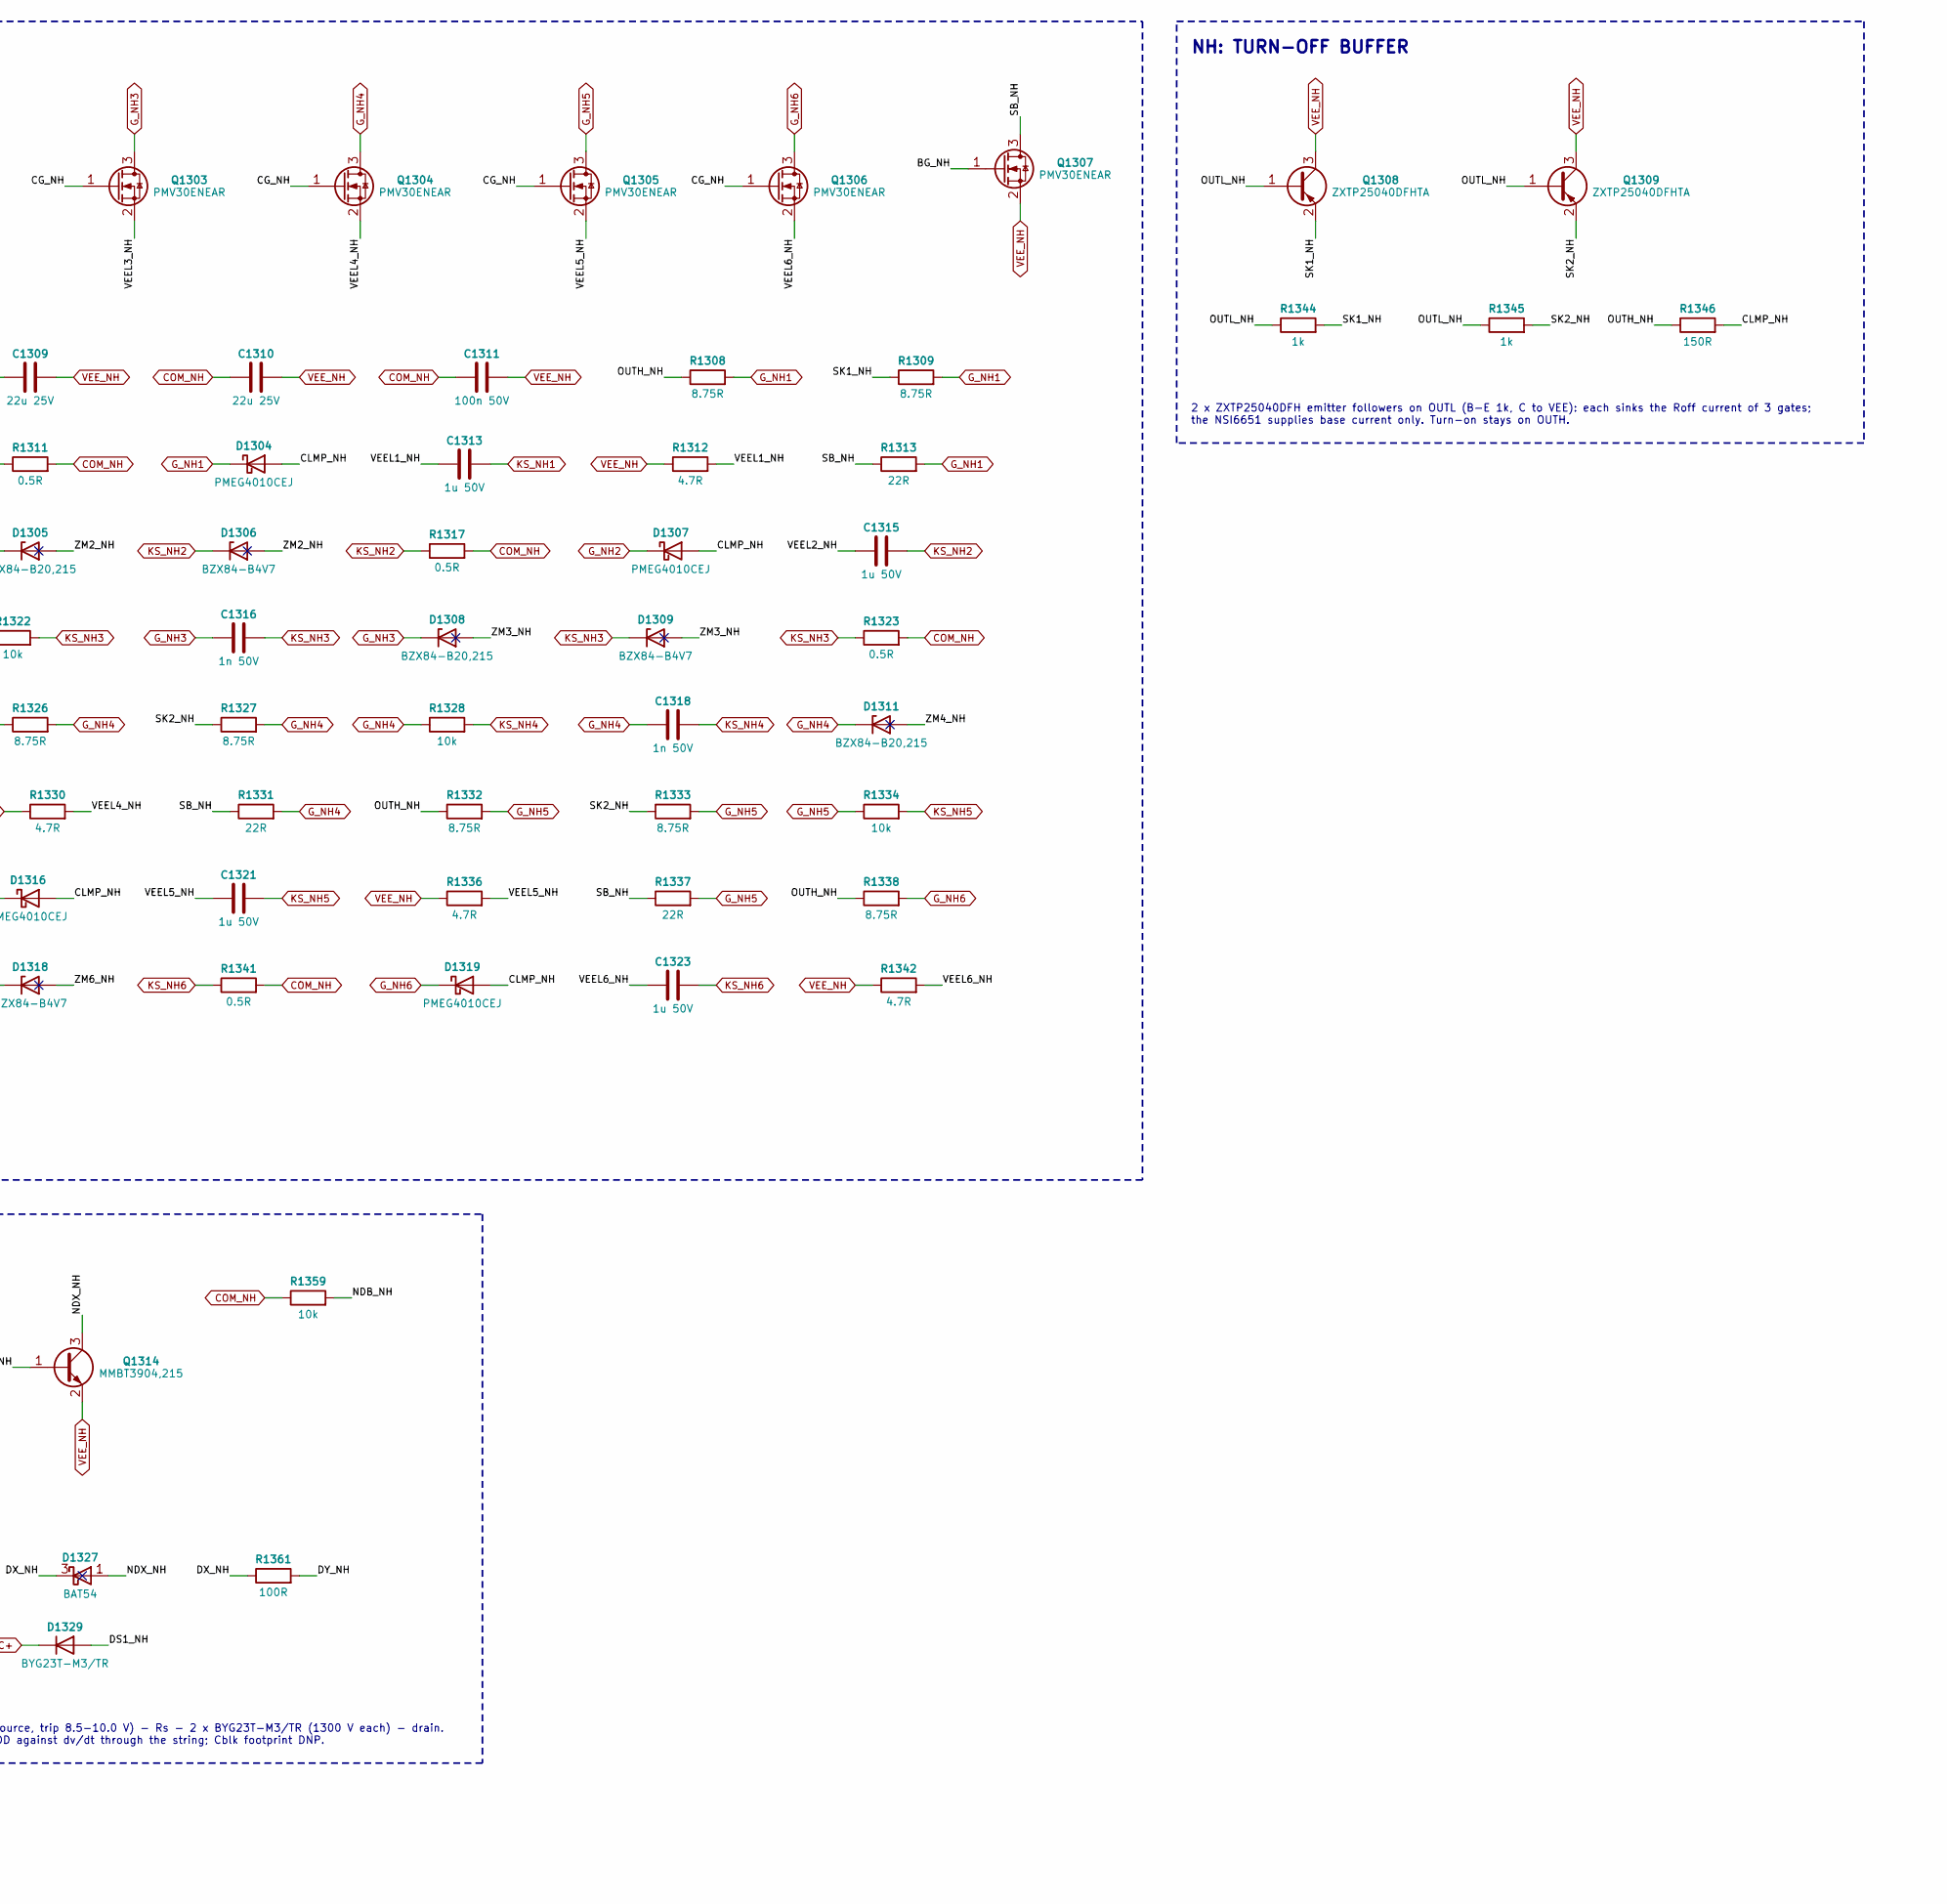
[picture p323: schematic 13_gdnh.kicad_sch, part in row 1, column 2]

Parts:
C1301, C1302, C1304: 100p 50V
C1303, C1306, C1308, C1311, C1324: 100n 50V
C1305: 1u 16V
C1307: 10u 50V
C1309, C1310: 22u 25V
C1312, C1314, C1316, C1318, C1320, C1322: 1n 50V
C1313, C1315, C1317, C1319, C1321, C1323: 1u 50V
C1325: 47p 50V
D1301, D1322, D1327: BAT54; MPN BAT54
D1302, D1305, D1308, D1311, D1314, D1317: BZX84-B20,215; MPN BZX84-B20,215
D1303, D1306, D1309, D1312, D1315, D1318: BZX84-B4V7; MPN BZX84-B4V7
D1304, D1307, D1310, D1313, D1316, D1319: PMEG4010CEJ; MPN PMEG4010CEJ
D1320, D1321: BZX84-B3V3; MPN BZX84-B3V3
D1323: BZX84-B5V6; MPN BZX84-B5V6
D1324, D1325: BZX84-B10; MPN BZX84-B10
D1326: BAT54S; MPN BAT54S
D1328, D1329: BYG23T-M3/TR; MPN BYG23T-M3/TR
Q1301, Q1302, Q1303, Q1304, Q1305, Q1306, Q1307: PMV30ENEAR; MPN PMV30ENEAR
Q1308, Q1309, Q1310: ZXTP25040DFHTA; MPN ZXTP25040DFHTA
Q1311: ZXTN25040DFHTA; MPN ZXTN25040DFHTA
Q1312, Q1314: MMBT3904,215; MPN MMBT3904,215
Q1313: MMBT3906,215; MPN MMBT3906,215
R1301, R1310, R1316, R1322, R1328, R1334, R1340, R1347, R1348, R1350, R1351, R1356, R1359: 10k
R1302, R1304, R1361: 100R
R1303: 3.65k
R1305: 0R
R1306: 0R; not fitted
R1307, R1344, R1345, R1358: 1k
R1308, R1309, R1314, R1315, R1320, R1321, R1326, R1327, R1332, R1333, R1338, R1339: 8.75R
R1311, R1317, R1323, R1329, R1335, R1341: 0.5R
R1312, R1318, R1324, R1330, R1336, R1342: 4.7R
R1313, R1319, R1325, R1331, R1337, R1343: 22R
R1346: 150R
R1349: 330R
R1352: 1.5k
R1353: 22k
R1354, R1360: 100k
R1355: 2.2k
R1357: 220R
U1301: SN74LVC1G17DBVR; MPN SN74LVC1G17DBVR
U1302: NSI6651ASC-Q1SWR; MPN NSI6651ASC-Q1SWR

Connections:
+5V: C1303.1, C1305.1, C1306.1, U1301.5 (VCC), U1302.15 (VCC1)
BG_NH: D1325.3 (K), Q1307.1 (G), R1357.2, R1358.1
BHB_NH: Q1313.1 (B), R1355.2, R1356.1
BHC_NH: Q1313.3 (C), R1357.1
BTB_NH: Q1312.1 (B), R1353.2, R1354.1
BTC_NH: Q1312.3 (C), R1355.1
BTZ_NH: D1324.1 (A), R1353.1
CG_NH: Q1301.1 (G), Q1302.1 (G), Q1303.1 (G), Q1304.1 (G), Q1305.1 (G), Q1306.1 (G), Q1310.3 (C), Q1311.3 (C), R1350.1
CLMP_NH: D1304.2 (A), D1307.2 (A), D1310.2 (A), D1313.2 (A), D1316.2 (A), D1319.2 (A), D1322.3 (K), R1346.2, U1302.7 (CLAMP)
COM_NH: C1307.2, C1308.2, C1309.1, C1310.1, C1311.1, C1324.2, D1320.1 (A), D1326.1 (A), Q1312.2 (E), R1306.2, R1311.2, R1317.2, R1323.2, R1329.2, R1335.2, R1341.2, R1354.2, R1359.1, U1302.3 (GND2)
DC+: D1329.1 (K)
DS1_NH: D1328.1 (K), D1329.2 (A)
DTB_NH: R1304.1, U1301.4 (Y)
DTS_NH: C1302.1, D1301.3 (K), R1303.2, U1301.2 (A)
DX_NH: D1324.3 (K), D1326.3 (COM), D1327.3 (K), R1361.1, U1302.2 (DESAT)
DY_NH: D1328.2 (A), R1361.2
EN5: U1302.14 (~RST/EN)
FLT_N: U1302.13 (~FLT)
GND: C1301.2, C1302.2, C1303.2, C1304.2, C1305.2, C1306.2, R1301.2, R1307.2, U1301.3 (GND), U1302.9 (GND1)
G_NH1: C1312.1, D1302.3 (K), D1304.1 (K), Q1301.3 (D), R1308.2, R1309.2, R1310.1, R1313.2
G_NH2: C1314.1, D1305.3 (K), D1307.1 (K), Q1302.3 (D), R1314.2, R1315.2, R1316.1, R1319.2
G_NH3: C1316.1, D1308.3 (K), D1310.1 (K), Q1303.3 (D), R1320.2, R1321.2, R1322.1, R1325.2
G_NH4: C1318.1, D1311.3 (K), D1313.1 (K), Q1304.3 (D), R1326.2, R1327.2, R1328.1, R1331.2
G_NH5: C1320.1, D1314.3 (K), D1316.1 (K), Q1305.3 (D), R1332.2, R1333.2, R1334.1, R1337.2
G_NH6: C1322.1, D1317.3 (K), D1319.1 (K), Q1306.3 (D), R1338.2, R1339.2, R1340.1, R1343.2
INN_NH: C1304.1, R1304.2, U1302.11 (IN-)
INP_NH: C1301.1, R1302.2, U1302.10 (IN+)
KS_NH1: C1312.2, C1313.2, D1303.3 (K), R1310.2, R1311.1
KS_NH2: C1314.2, C1315.2, D1306.3 (K), R1316.2, R1317.1
KS_NH3: C1316.2, C1317.2, D1309.3 (K), R1322.2, R1323.1
KS_NH4: C1318.2, C1319.2, D1312.3 (K), R1328.2, R1329.1
KS_NH5: C1320.2, C1321.2, D1315.3 (K), R1334.2, R1335.1
KS_NH6: C1322.2, C1323.2, D1318.3 (K), R1340.2, R1341.1
NDB_NH: Q1314.1 (B), R1359.2
NDX_NH: D1327.1 (A), Q1314.3 (C), R1360.2
OUTH_NH: D1323.3 (K), R1308.1, R1314.1, R1320.1, R1326.1, R1332.1, R1338.1, R1346.1, U1302.4 (OUTH)
OUTL_NH: Q1308.1 (B), Q1309.1 (B), R1344.1, R1345.1, U1302.6 (OUTL)
P1_NH: R1305.1, R1306.1, U1302.1 (VEE2)
P16_NH: R1307.1, U1302.16 (TEST)
PWM7_5V: R1301.1, R1302.1
PWM8_5V: D1301.1 (A), R1303.1
QIB_NH: Q1310.1 (B), R1348.2, R1349.1
QID_NH: D1321.3 (K), R1349.2
QIZ_NH: D1321.1 (A), D1322.1 (A)
QRB_NH: C1325.2, Q1311.1 (B), R1351.1, R1352.2
QRZ_NH: C1325.1, D1323.1 (A), R1352.1
RDY: U1302.12 (RDY)
SB_NH: Q1307.3 (D), R1313.1, R1319.1, R1325.1, R1331.1, R1337.1, R1343.1
SK1_NH: Q1308.2 (E), R1309.1, R1315.1, R1321.1, R1344.2
SK2_NH: Q1309.2 (E), R1327.1, R1333.1, R1339.1, R1345.2
VCG_NH: C1324.1, D1320.3 (K), Q1310.2 (E), R1347.2, R1348.1
VDD_NH: C1307.1, C1308.1, D1326.2 (K), Q1313.2 (E), R1347.1, R1356.2, R1360.1, U1302.5 (VCC2)
VEEL1_NH: C1313.1, Q1301.2 (S), R1312.2
VEEL2_NH: C1315.1, Q1302.2 (S), R1318.2
VEEL3_NH: C1317.1, Q1303.2 (S), R1324.2
VEEL4_NH: C1319.1, Q1304.2 (S), R1330.2
VEEL5_NH: C1321.1, Q1305.2 (S), R1336.2
VEEL6_NH: C1323.1, Q1306.2 (S), R1342.2
VEE_NH: C1309.2, C1310.2, C1311.2, D1325.1 (A), Q1307.2 (S), Q1308.3 (C), Q1309.3 (C), Q1311.2 (E), Q1314.2 (E), R1305.2, R1312.1, R1318.1, R1324.1, R1330.1, R1336.1, R1342.1, R1350.2, R1351.2, R1358.2, U1302.8 (VEE2)
ZM1_NH: D1302.1 (A), D1303.1 (A)
ZM2_NH: D1305.1 (A), D1306.1 (A)
ZM3_NH: D1308.1 (A), D1309.1 (A)
ZM4_NH: D1311.1 (A), D1312.1 (A)
ZM5_NH: D1314.1 (A), D1315.1 (A)
ZM6_NH: D1317.1 (A), D1318.1 (A)

Notes on the sheet:
IN+ = own PWM; IN- = complementary switch, falling edge stretched 3.65k/100p (interlock + min dead time = max(firmware, hardware)). Bias PG (active low) pulls RDY low.
Per device: Ron/Roff, 0.5R Kelvin R to the COM star, 10k and Zeners (about +21 V / -5.7 V) on its own Kelvin net. Miller hold: N-MOSFET clamp (PMV30ENEA) gate-pin to a local VEE (1u on the Kelvin pin). LAYOUT: FET + 1u at the device, loop <= 1 nH.
MMBT3906 inverter (E COM, base BAT54+2.2k on CLAMP) drives CG to COM once the lowest gate is below ~-1.2 V; MMBT3904 release (from OUTH via 5.6 V Zener) holds CG at VEE while OUTH drives.
2 x ZXTP25040DFH emitter followers on OUTL (B-E 1k, C to VEE): each sinks the Roff current of 3 gates; the NSI6651 supplies base current only. Turn-on stays on OUTH.
NH: DRIVER AND 6 GATES
DESAT > 10.3-10.9 V (above the 10.0 V maximum trip of the -Q1 grade) -> MMBT3904 -> MMBT3906 charges BG to VEE + 10 V; per device AO3400A + 22R pull the gate to VEE; BG holds ~3 us (1k + FET gates).
NH: MILLER CLAMP CONTROL
NH: LOGIC SIDE
NH: DESAT
NH: SHORT-CIRCUIT BOOSTER
NH: TURN-OFF BUFFER
DESAT pin (internal 500 uA blanking source, trip 8.5-10.0 V) - Rs - 2 x BYG23T-M3/TR (1300 V each) - drain. BAT54S keeps DX between COM and VDD against dv/dt through the string; Cblk footprint DNP.
