vectivolt/PCM/hardware/PCS-PWR-4W/sheets/14_gdnl.kicad_sch

## KiCad design hardware/PCS-PWR-4W/sheets/14_gdnl.kicad_sch (2026-10-07)

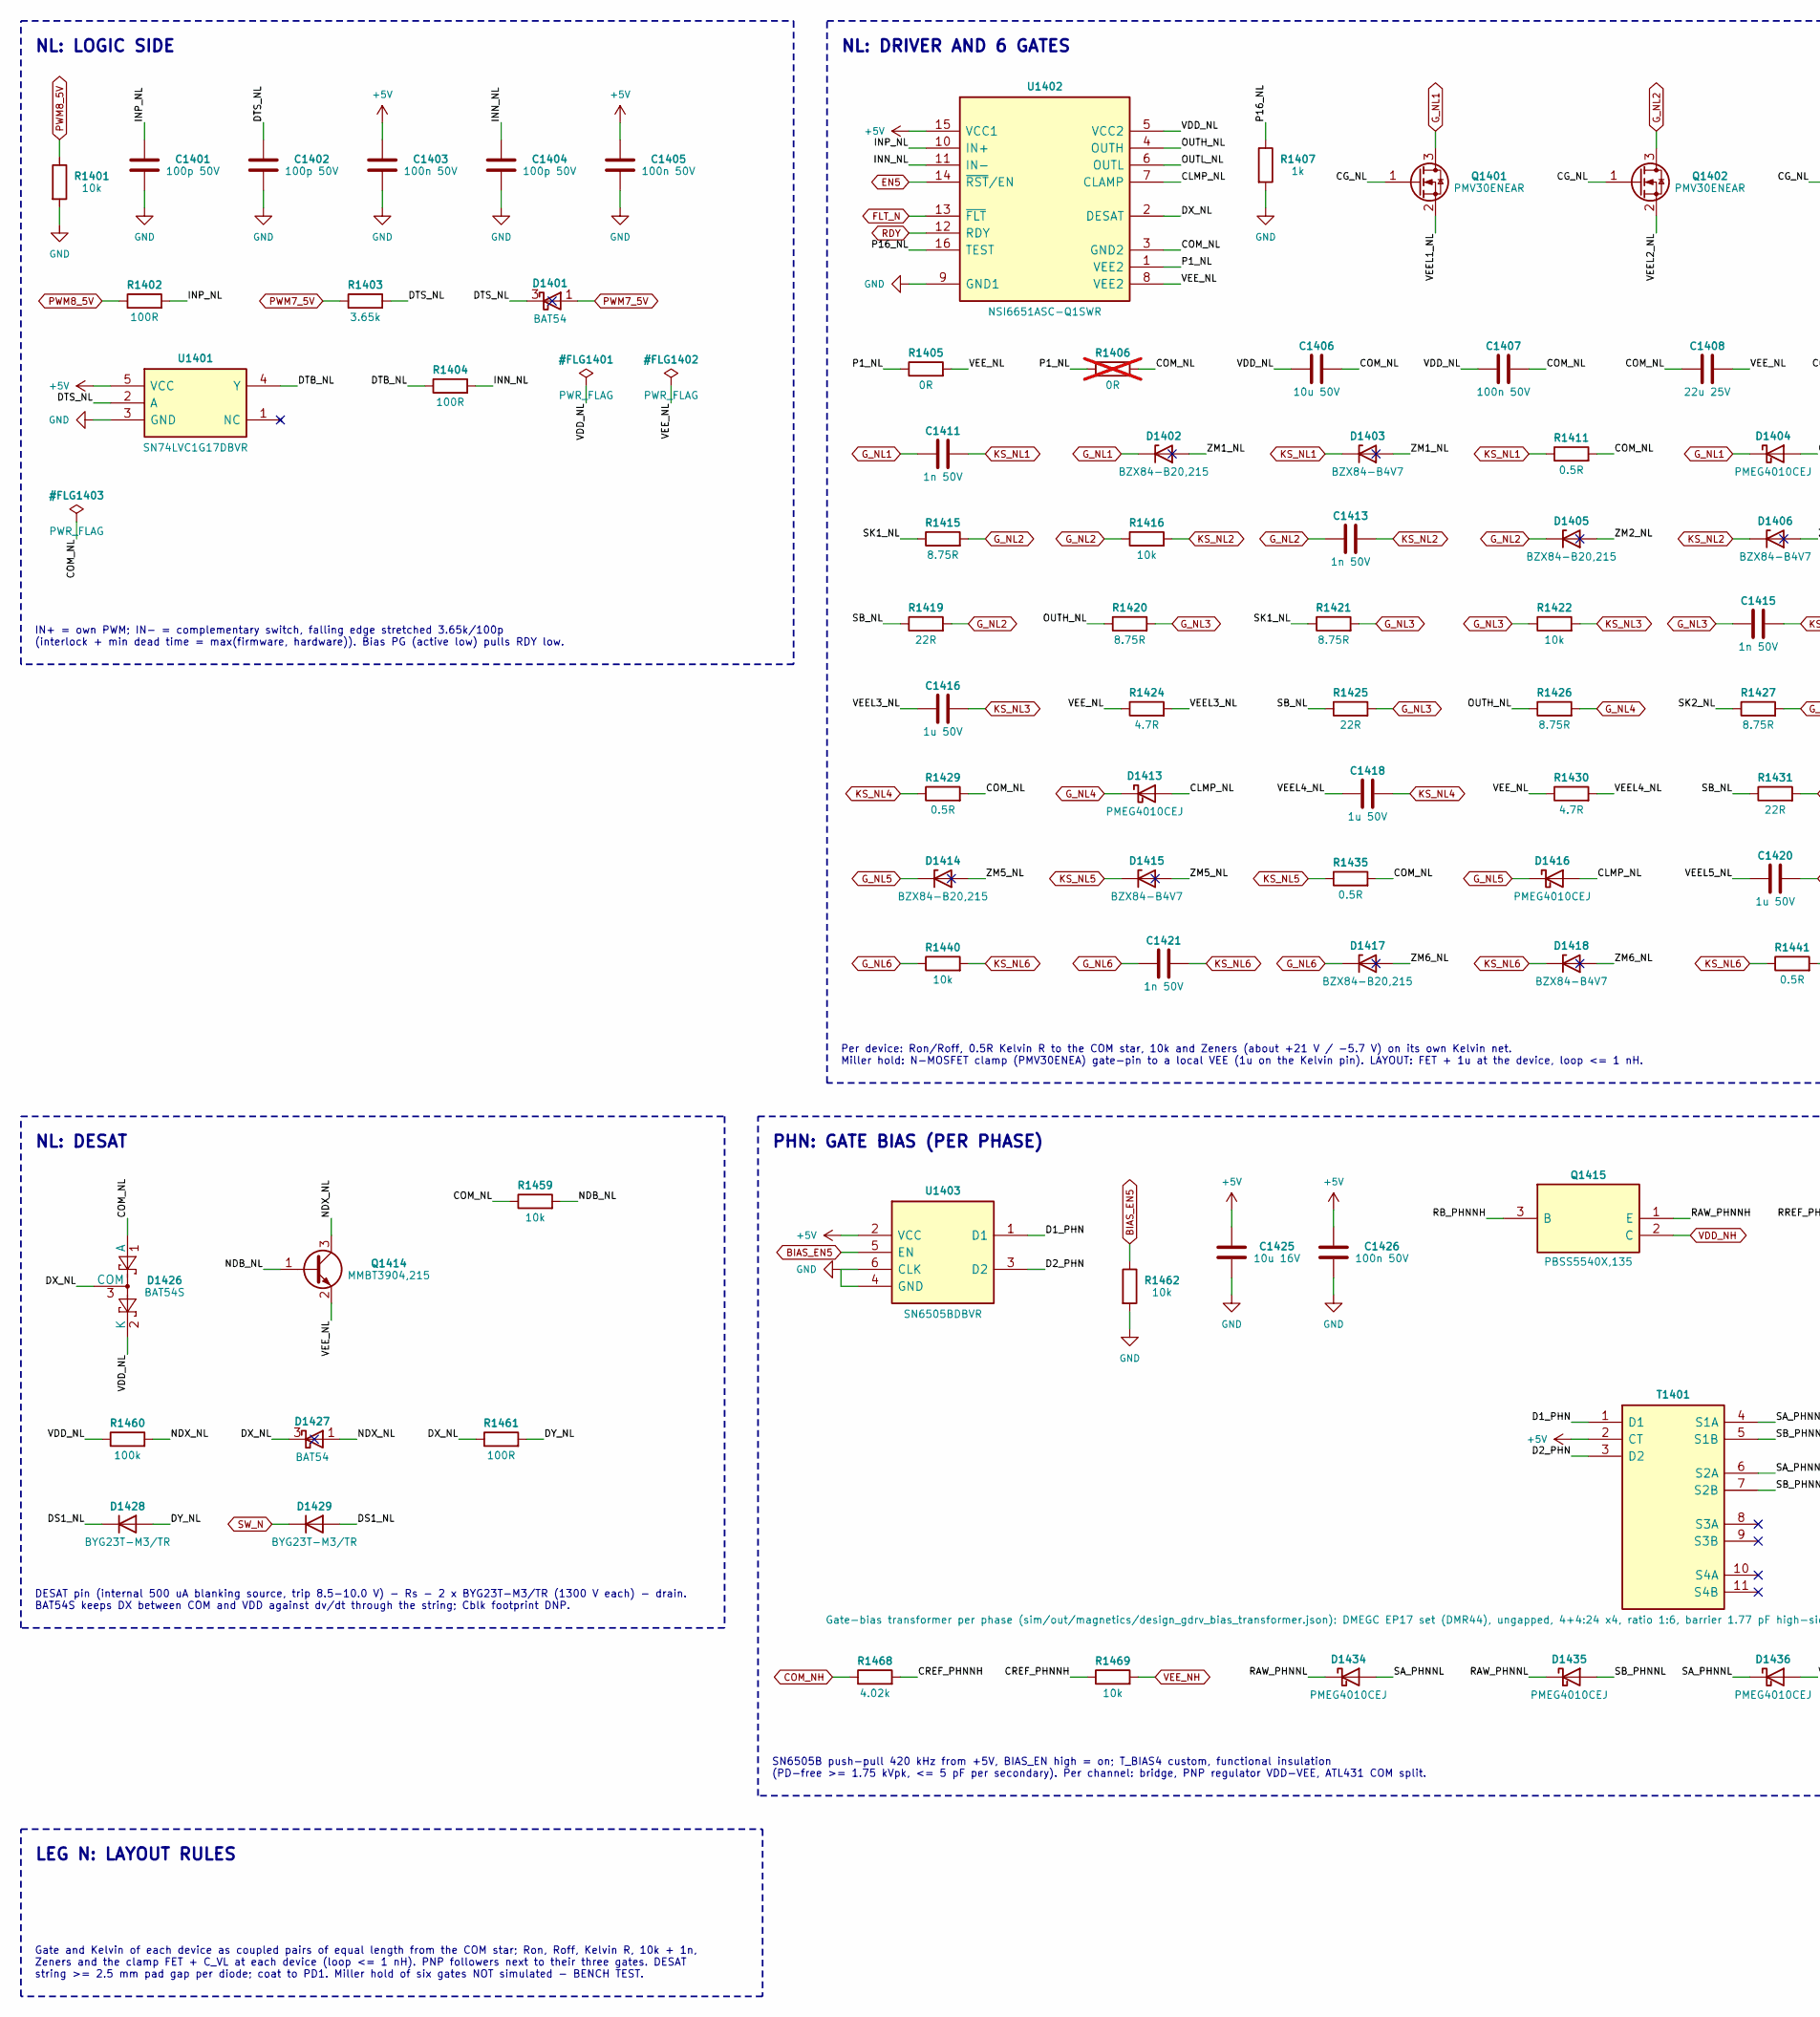
[picture p324: schematic 14_gdnl.kicad_sch, part in row 1, column 1]

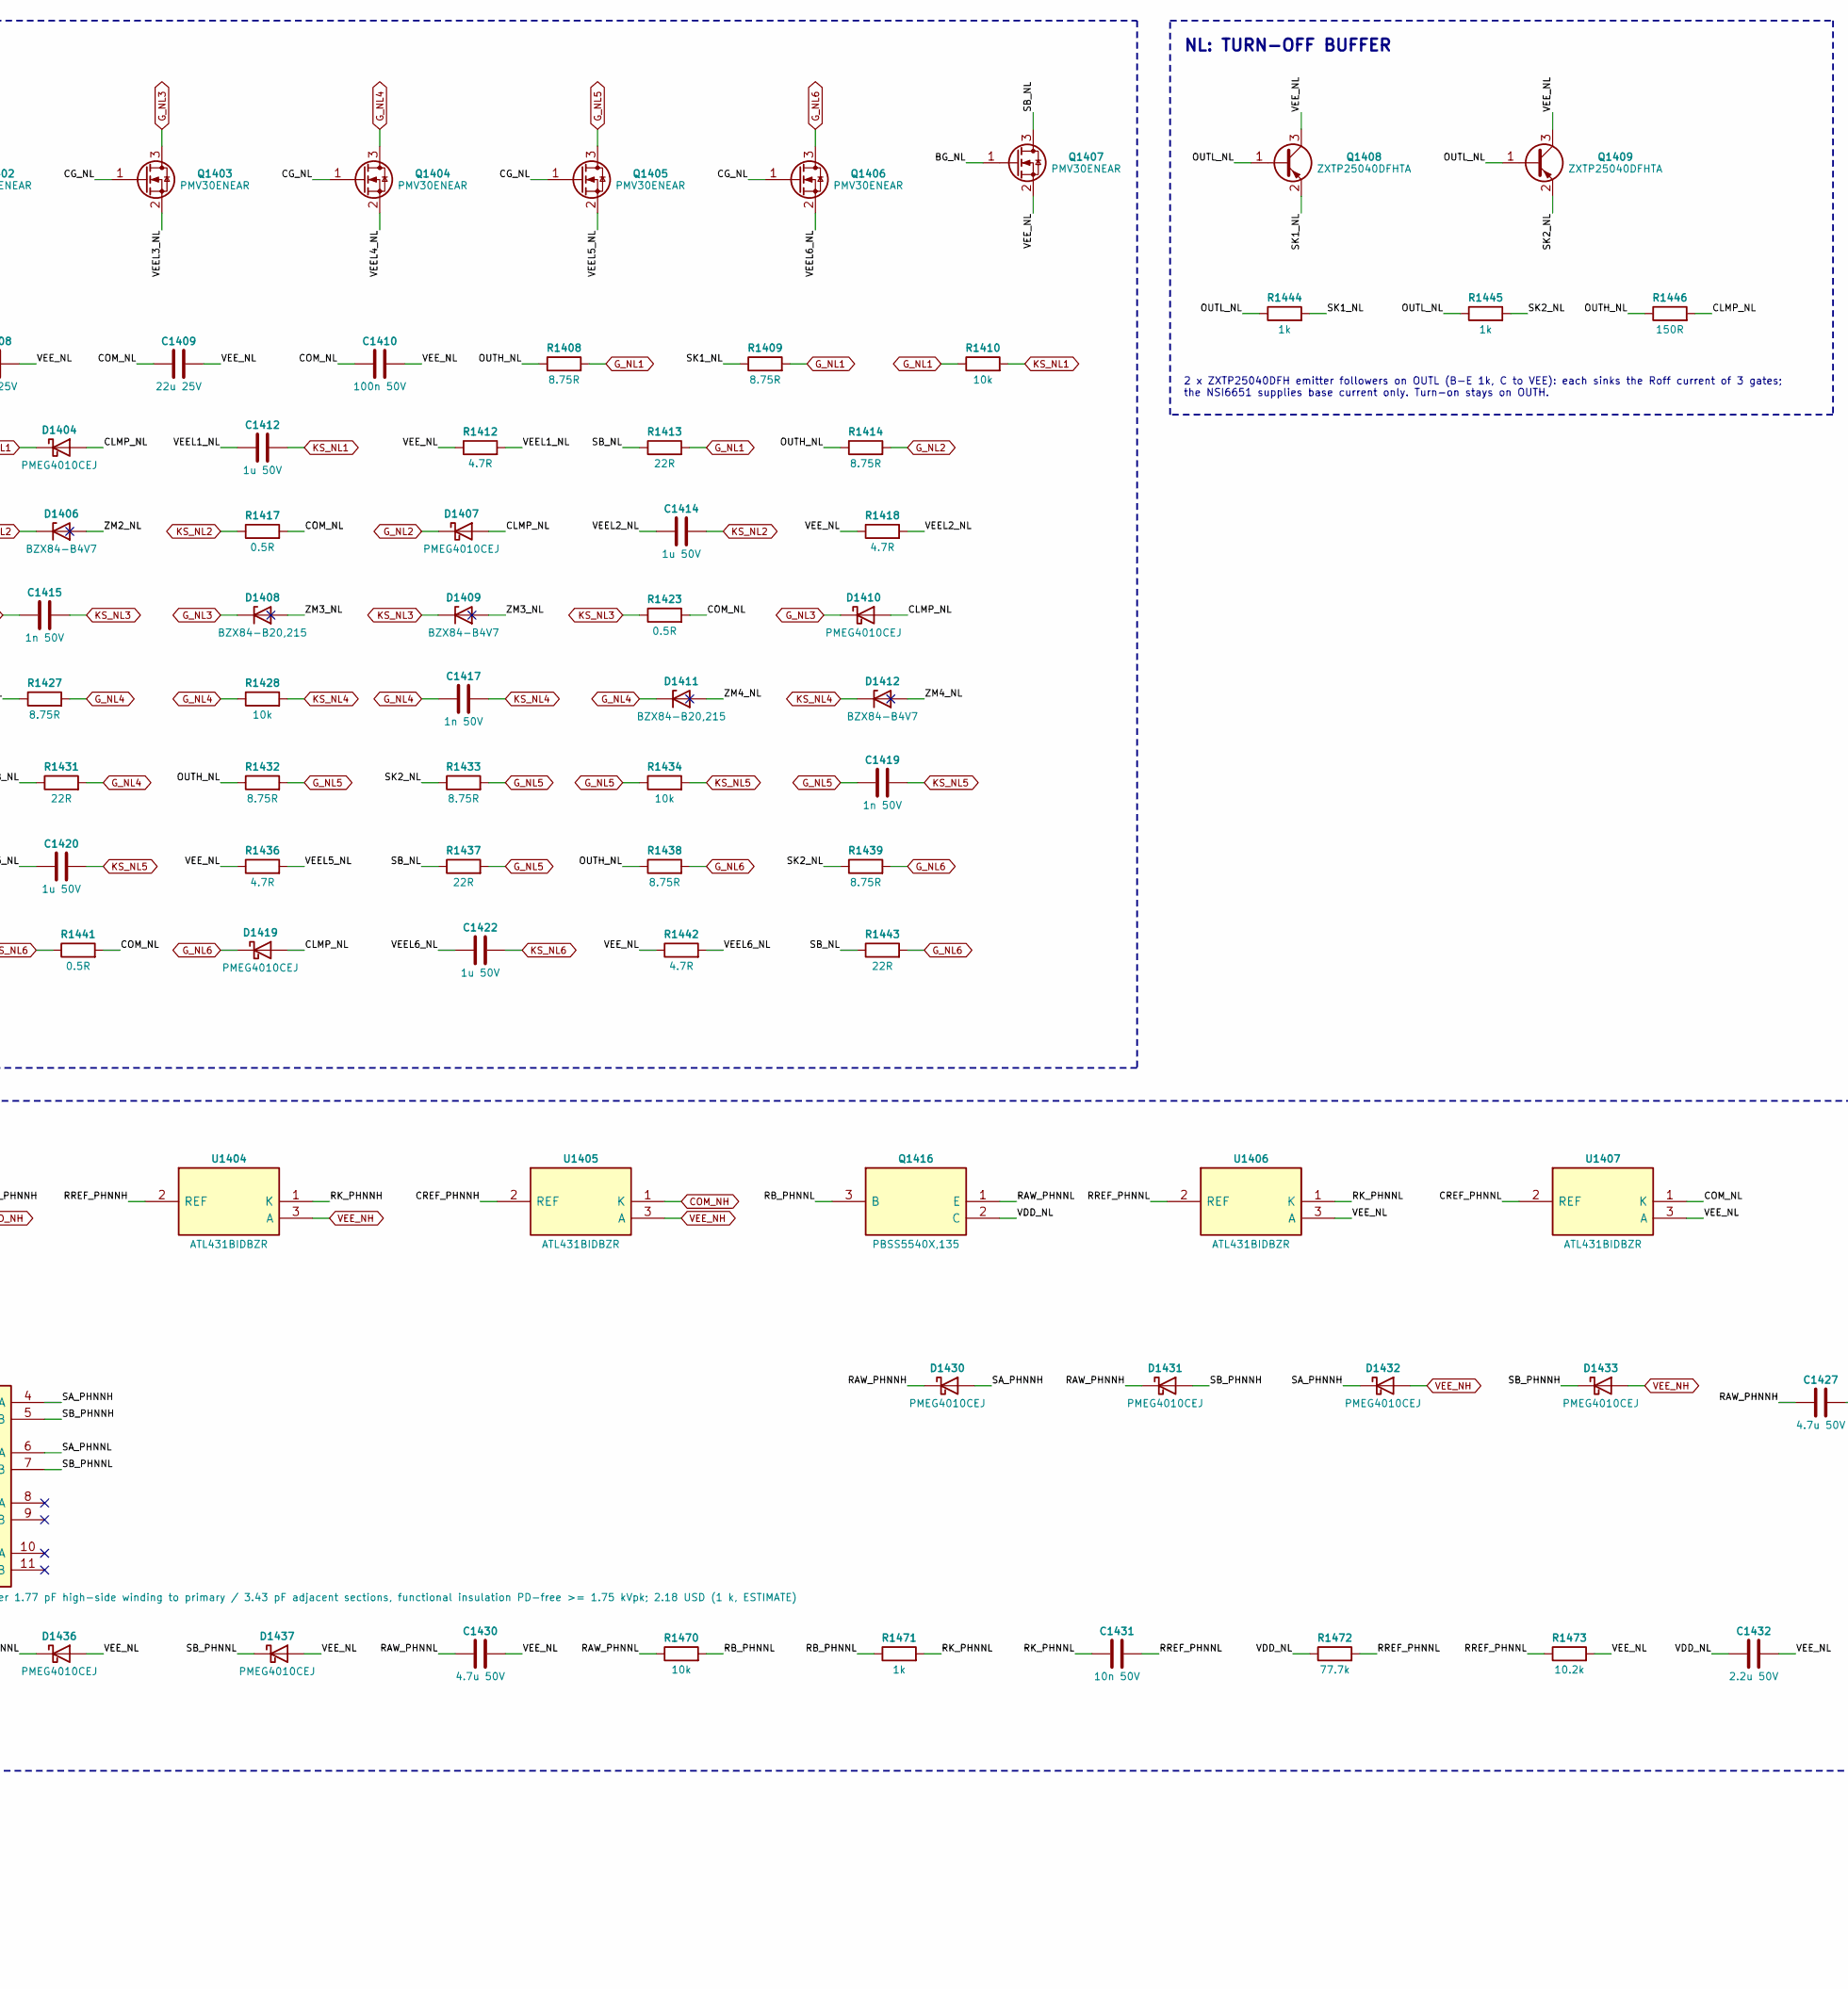
[picture p325: schematic 14_gdnl.kicad_sch, part in row 1, column 2]

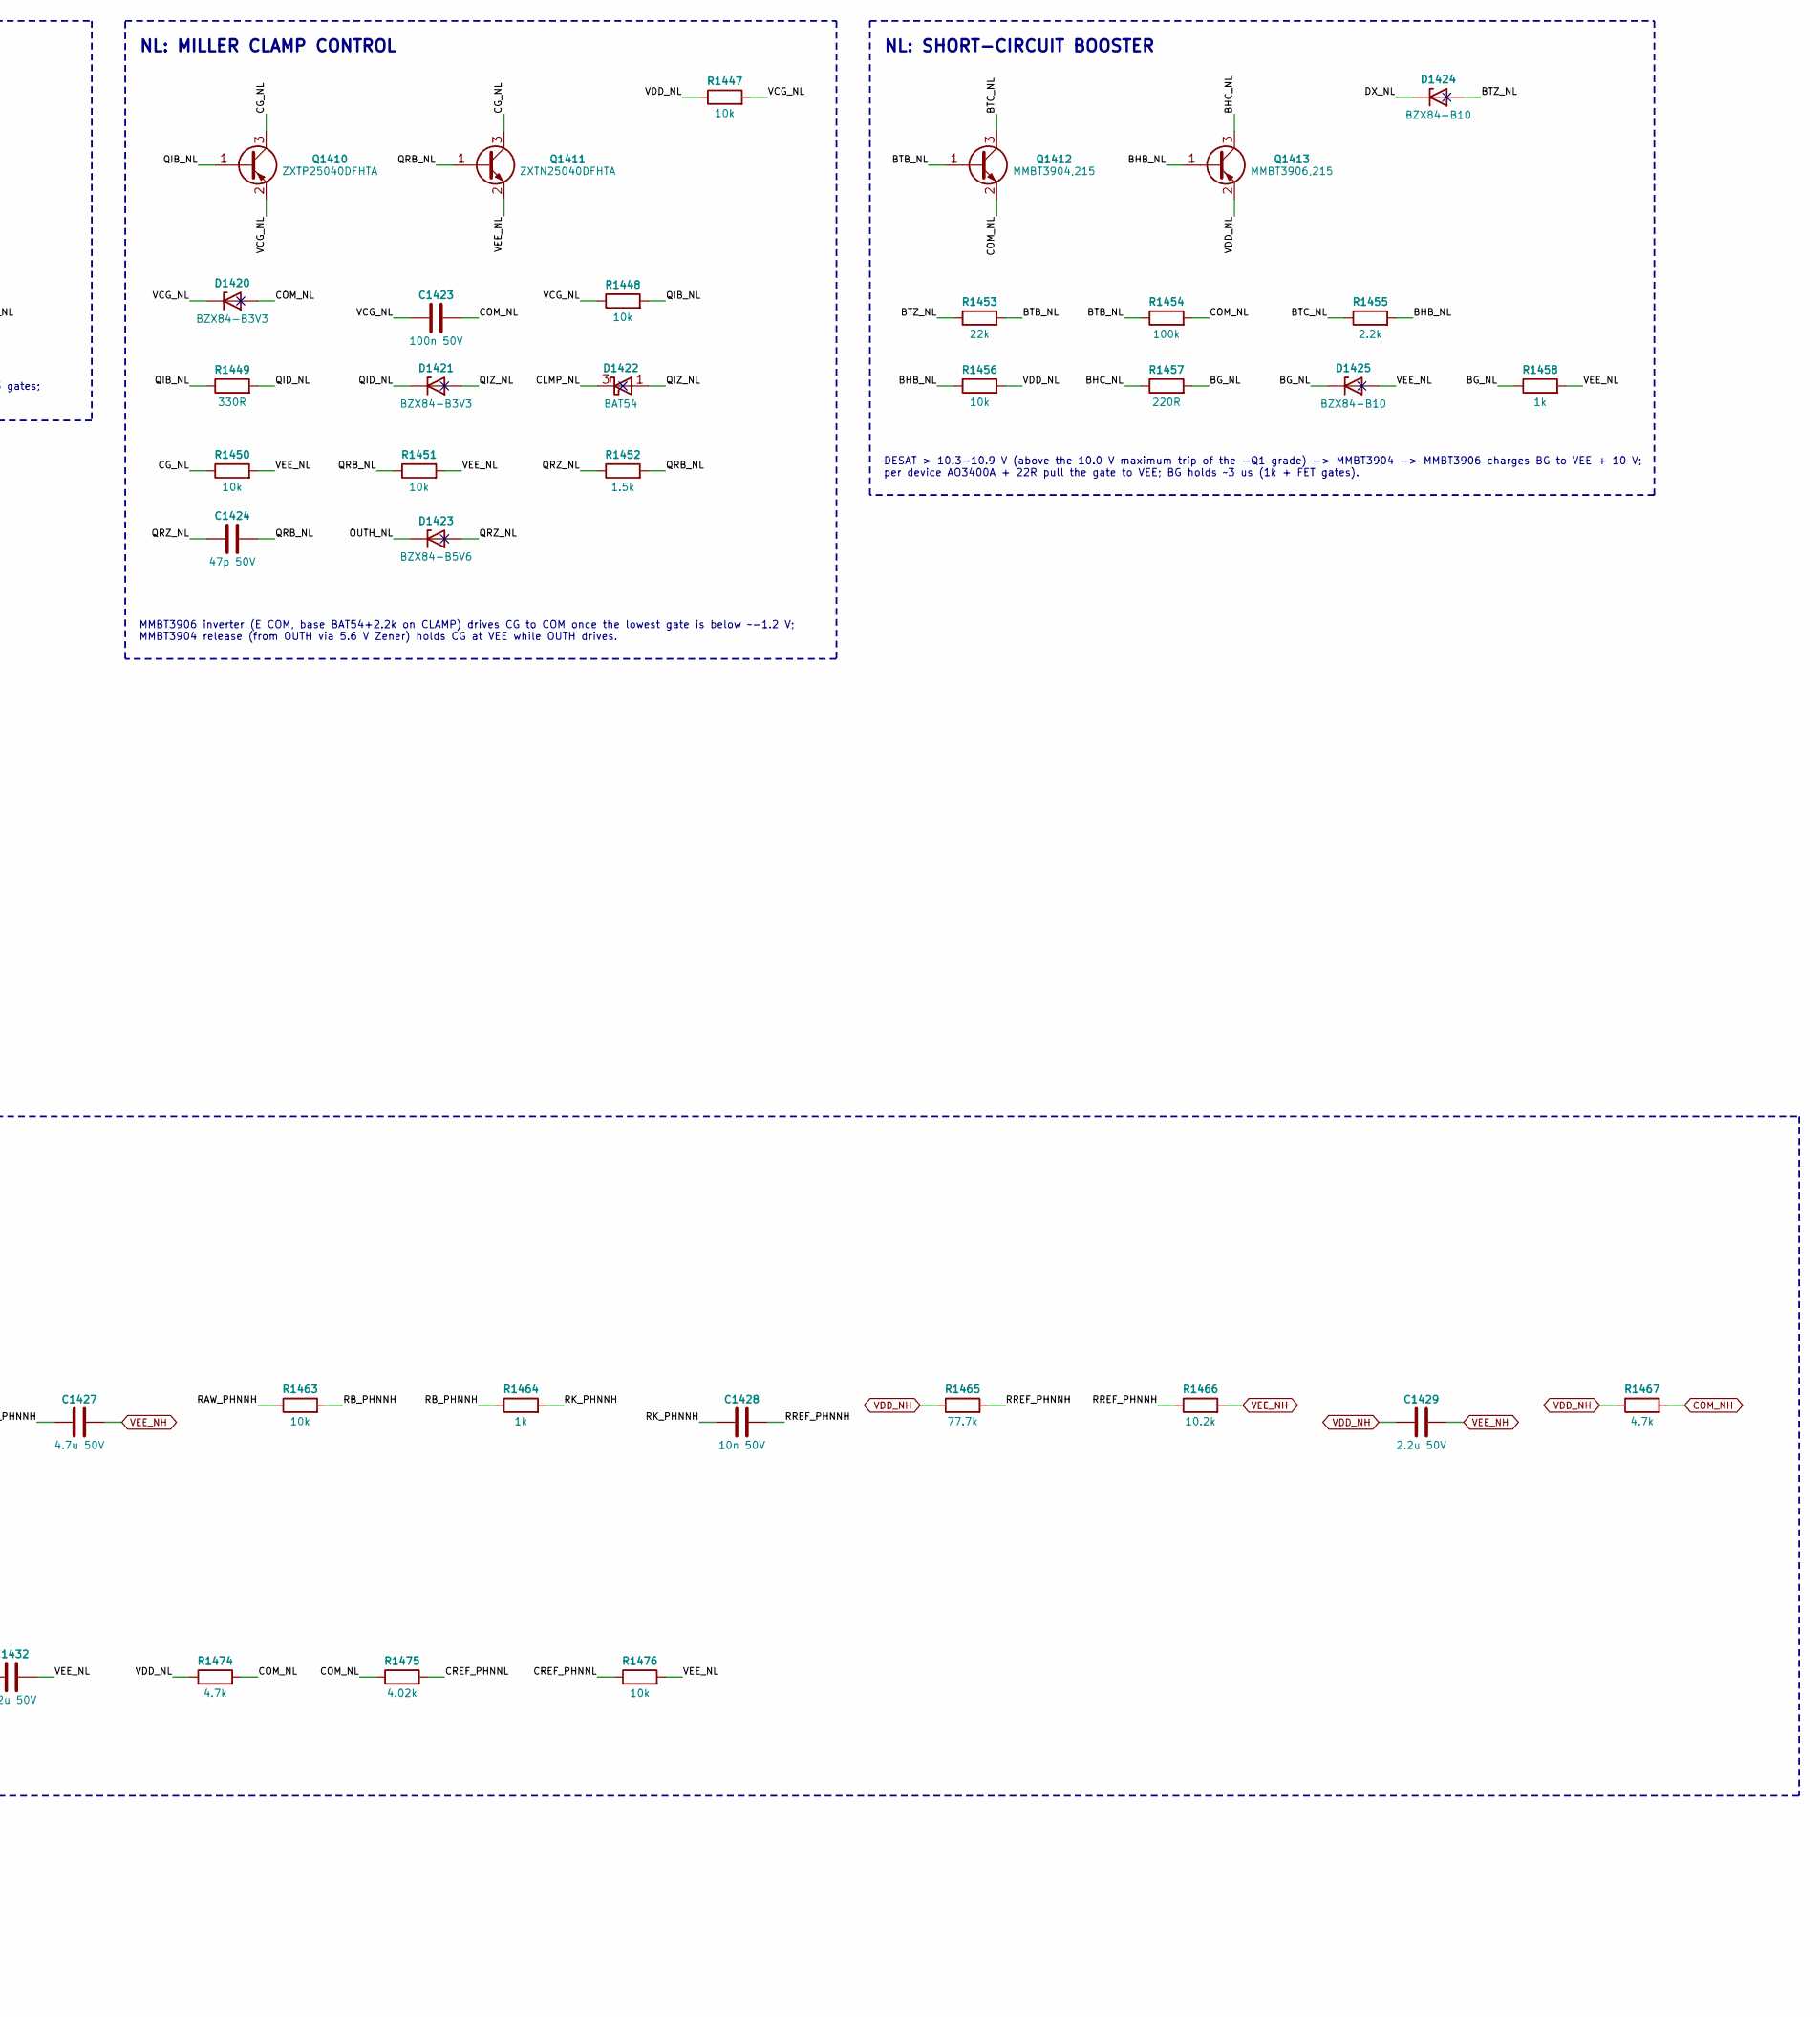
[picture p326: schematic 14_gdnl.kicad_sch, part in row 1, column 3]

Parts:
C1401, C1402, C1404: 100p 50V
C1403, C1405, C1407, C1410, C1423, C1426: 100n 50V
C1406: 10u 50V
C1408, C1409: 22u 25V
C1411, C1413, C1415, C1417, C1419, C1421: 1n 50V
C1412, C1414, C1416, C1418, C1420, C1422: 1u 50V
C1424: 47p 50V
C1425: 10u 16V
C1427, C1430: 4.7u 50V
C1428, C1431: 10n 50V
C1429, C1432: 2.2u 50V
D1401, D1422, D1427: BAT54; MPN BAT54
D1402, D1405, D1408, D1411, D1414, D1417: BZX84-B20,215; MPN BZX84-B20,215
D1403, D1406, D1409, D1412, D1415, D1418: BZX84-B4V7; MPN BZX84-B4V7
D1404, D1407, D1410, D1413, D1416, D1419, D1430, D1431, D1432, D1433, D1434, D1435, D1436, D1437: PMEG4010CEJ; MPN PMEG4010CEJ
D1420, D1421: BZX84-B3V3; MPN BZX84-B3V3
D1423: BZX84-B5V6; MPN BZX84-B5V6
D1424, D1425: BZX84-B10; MPN BZX84-B10
D1426: BAT54S; MPN BAT54S
D1428, D1429: BYG23T-M3/TR; MPN BYG23T-M3/TR
Q1401, Q1402, Q1403, Q1404, Q1405, Q1406, Q1407: PMV30ENEAR; MPN PMV30ENEAR
Q1408, Q1409, Q1410: ZXTP25040DFHTA; MPN ZXTP25040DFHTA
Q1411: ZXTN25040DFHTA; MPN ZXTN25040DFHTA
Q1412, Q1414: MMBT3904,215; MPN MMBT3904,215
Q1413: MMBT3906,215; MPN MMBT3906,215
Q1415, Q1416: PBSS5540X,135; MPN PBSS5540X,135
R1401, R1410, R1416, R1422, R1428, R1434, R1440, R1447, R1448, R1450, R1451, R1456, R1459, R1462, R1463, R1469, R1470, R1476: 10k
R1402, R1404, R1461: 100R
R1403: 3.65k
R1405: 0R
R1406: 0R; not fitted
R1407, R1444, R1445, R1458, R1464, R1471: 1k
R1408, R1409, R1414, R1415, R1420, R1421, R1426, R1427, R1432, R1433, R1438, R1439: 8.75R
R1411, R1417, R1423, R1429, R1435, R1441: 0.5R
R1412, R1418, R1424, R1430, R1436, R1442: 4.7R
R1413, R1419, R1425, R1431, R1437, R1443: 22R
R1446: 150R
R1449: 330R
R1452: 1.5k
R1453: 22k
R1454, R1460: 100k
R1455: 2.2k
R1457: 220R
R1465, R1472: 77.7k
R1466, R1473: 10.2k
R1467, R1474: 4.7k
R1468, R1475: 4.02k
T1401: Gate-bias transformer per phase (sim/out/magnetic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
U1401: SN74LVC1G17DBVR; MPN SN74LVC1G17DBVR
U1402: NSI6651ASC-Q1SWR; MPN NSI6651ASC-Q1SWR
U1403: SN6505BDBVR; MPN SN6505BDBVR
U1404, U1405, U1406, U1407: ATL431BIDBZR; MPN ATL431BIDBZR

Connections:
+5V: C1403.1, C1405.1, C1425.1, C1426.1, T1401.2 (CT), U1401.5 (VCC), U1402.15 (VCC1), U1403.2 (VCC)
BG_NL: D1425.3 (K), Q1407.1 (G), R1457.2, R1458.1
BHB_NL: Q1413.1 (B), R1455.2, R1456.1
BHC_NL: Q1413.3 (C), R1457.1
BIAS_EN5: R1462.1, U1403.5 (EN)
BTB_NL: Q1412.1 (B), R1453.2, R1454.1
BTC_NL: Q1412.3 (C), R1455.1
BTZ_NL: D1424.1 (A), R1453.1
CG_NL: Q1401.1 (G), Q1402.1 (G), Q1403.1 (G), Q1404.1 (G), Q1405.1 (G), Q1406.1 (G), Q1410.3 (C), Q1411.3 (C), R1450.1
CLMP_NL: D1404.2 (A), D1407.2 (A), D1410.2 (A), D1413.2 (A), D1416.2 (A), D1419.2 (A), D1422.3 (K), R1446.2, U1402.7 (CLAMP)
COM_NH: R1467.2, R1468.1, U1405.1 (K)
COM_NL: C1406.2, C1407.2, C1408.1, C1409.1, C1410.1, C1423.2, D1420.1 (A), D1426.1 (A), Q1412.2 (E), R1406.2, R1411.2, R1417.2, R1423.2, R1429.2, R1435.2, R1441.2, R1454.2, R1459.1, R1474.2, R1475.1, U1402.3 (GND2), U1407.1 (K)
CREF_PHNNH: R1468.2, R1469.1, U1405.2 (REF)
CREF_PHNNL: R1475.2, R1476.1, U1407.2 (REF)
D1_PHN: T1401.1 (D1), U1403.1 (D1)
D2_PHN: T1401.3 (D2), U1403.3 (D2)
DS1_NL: D1428.1 (K), D1429.2 (A)
DTB_NL: R1404.1, U1401.4 (Y)
DTS_NL: C1402.1, D1401.3 (K), R1403.2, U1401.2 (A)
DX_NL: D1424.3 (K), D1426.3 (COM), D1427.3 (K), R1461.1, U1402.2 (DESAT)
DY_NL: D1428.2 (A), R1461.2
EN5: U1402.14 (~RST/EN)
FLT_N: U1402.13 (~FLT)
GND: C1401.2, C1402.2, C1403.2, C1404.2, C1405.2, C1425.2, C1426.2, R1401.2, R1407.2, R1462.2, U1401.3 (GND), U1402.9 (GND1), U1403.4 (GND), U1403.6 (CLK)
G_NL1: C1411.1, D1402.3 (K), D1404.1 (K), Q1401.3 (D), R1408.2, R1409.2, R1410.1, R1413.2
G_NL2: C1413.1, D1405.3 (K), D1407.1 (K), Q1402.3 (D), R1414.2, R1415.2, R1416.1, R1419.2
G_NL3: C1415.1, D1408.3 (K), D1410.1 (K), Q1403.3 (D), R1420.2, R1421.2, R1422.1, R1425.2
G_NL4: C1417.1, D1411.3 (K), D1413.1 (K), Q1404.3 (D), R1426.2, R1427.2, R1428.1, R1431.2
G_NL5: C1419.1, D1414.3 (K), D1416.1 (K), Q1405.3 (D), R1432.2, R1433.2, R1434.1, R1437.2
G_NL6: C1421.1, D1417.3 (K), D1419.1 (K), Q1406.3 (D), R1438.2, R1439.2, R1440.1, R1443.2
INN_NL: C1404.1, R1404.2, U1402.11 (IN-)
INP_NL: C1401.1, R1402.2, U1402.10 (IN+)
KS_NL1: C1411.2, C1412.2, D1403.3 (K), R1410.2, R1411.1
KS_NL2: C1413.2, C1414.2, D1406.3 (K), R1416.2, R1417.1
KS_NL3: C1415.2, C1416.2, D1409.3 (K), R1422.2, R1423.1
KS_NL4: C1417.2, C1418.2, D1412.3 (K), R1428.2, R1429.1
KS_NL5: C1419.2, C1420.2, D1415.3 (K), R1434.2, R1435.1
KS_NL6: C1421.2, C1422.2, D1418.3 (K), R1440.2, R1441.1
NDB_NL: Q1414.1 (B), R1459.2
NDX_NL: D1427.1 (A), Q1414.3 (C), R1460.2
OUTH_NL: D1423.3 (K), R1408.1, R1414.1, R1420.1, R1426.1, R1432.1, R1438.1, R1446.1, U1402.4 (OUTH)
OUTL_NL: Q1408.1 (B), Q1409.1 (B), R1444.1, R1445.1, U1402.6 (OUTL)
P1_NL: R1405.1, R1406.1, U1402.1 (VEE2)
P16_NL: R1407.1, U1402.16 (TEST)
PWM7_5V: D1401.1 (A), R1403.1
PWM8_5V: R1401.1, R1402.1
QIB_NL: Q1410.1 (B), R1448.2, R1449.1
QID_NL: D1421.3 (K), R1449.2
QIZ_NL: D1421.1 (A), D1422.1 (A)
QRB_NL: C1424.2, Q1411.1 (B), R1451.1, R1452.2
QRZ_NL: C1424.1, D1423.1 (A), R1452.1
RAW_PHNNH: C1427.1, D1430.1 (K), D1431.1 (K), Q1415.1 (E), R1463.1
RAW_PHNNL: C1430.1, D1434.1 (K), D1435.1 (K), Q1416.1 (E), R1470.1
RB_PHNNH: Q1415.3 (B), R1463.2, R1464.1
RB_PHNNL: Q1416.3 (B), R1470.2, R1471.1
RDY: U1402.12 (RDY)
RK_PHNNH: C1428.1, R1464.2, U1404.1 (K)
RK_PHNNL: C1431.1, R1471.2, U1406.1 (K)
RREF_PHNNH: C1428.2, R1465.2, R1466.1, U1404.2 (REF)
RREF_PHNNL: C1431.2, R1472.2, R1473.1, U1406.2 (REF)
SA_PHNNH: D1430.2 (A), D1432.1 (K), T1401.4 (S1A)
SA_PHNNL: D1434.2 (A), D1436.1 (K), T1401.6 (S2A)
SB_NL: Q1407.3 (D), R1413.1, R1419.1, R1425.1, R1431.1, R1437.1, R1443.1
SB_PHNNH: D1431.2 (A), D1433.1 (K), T1401.5 (S1B)
SB_PHNNL: D1435.2 (A), D1437.1 (K), T1401.7 (S2B)
SK1_NL: Q1408.2 (E), R1409.1, R1415.1, R1421.1, R1444.2
SK2_NL: Q1409.2 (E), R1427.1, R1433.1, R1439.1, R1445.2
SW_N: D1429.1 (K)
VCG_NL: C1423.1, D1420.3 (K), Q1410.2 (E), R1447.2, R1448.1
VDD_NH: C1429.1, Q1415.2 (C), R1465.1, R1467.1
VDD_NL: C1406.1, C1407.1, C1432.1, D1426.2 (K), Q1413.2 (E), Q1416.2 (C), R1447.1, R1456.2, R1460.1, R1472.1, R1474.1, U1402.5 (VCC2)
VEEL1_NL: C1412.1, Q1401.2 (S), R1412.2
VEEL2_NL: C1414.1, Q1402.2 (S), R1418.2
VEEL3_NL: C1416.1, Q1403.2 (S), R1424.2
VEEL4_NL: C1418.1, Q1404.2 (S), R1430.2
VEEL5_NL: C1420.1, Q1405.2 (S), R1436.2
VEEL6_NL: C1422.1, Q1406.2 (S), R1442.2
VEE_NH: C1427.2, C1429.2, D1432.2 (A), D1433.2 (A), R1466.2, R1469.2, U1404.3 (A), U1405.3 (A)
VEE_NL: C1408.2, C1409.2, C1410.2, C1430.2, C1432.2, D1425.1 (A), D1436.2 (A), D1437.2 (A), Q1407.2 (S), Q1408.3 (C), Q1409.3 (C), Q1411.2 (E), Q1414.2 (E), R1405.2, R1412.1, R1418.1, R1424.1, R1430.1, R1436.1, R1442.1, R1450.2, R1451.2, R1458.2, R1473.2, R1476.2, U1402.8 (VEE2), U1406.3 (A), U1407.3 (A)
ZM1_NL: D1402.1 (A), D1403.1 (A)
ZM2_NL: D1405.1 (A), D1406.1 (A)
ZM3_NL: D1408.1 (A), D1409.1 (A)
ZM4_NL: D1411.1 (A), D1412.1 (A)
ZM5_NL: D1414.1 (A), D1415.1 (A)
ZM6_NL: D1417.1 (A), D1418.1 (A)

Notes on the sheet:
PHN: GATE BIAS (PER PHASE)
IN+ = own PWM; IN- = complementary switch, falling edge stretched 3.65k/100p (interlock + min dead time = max(firmware, hardware)). Bias PG (active low) pulls RDY low.
NL: DRIVER AND 6 GATES
NL: DESAT
2 x ZXTP25040DFH emitter followers on OUTL (B-E 1k, C to VEE): each sinks the Roff current of 3 gates; the NSI6651 supplies base current only. Turn-on stays on OUTH.
NL: SHORT-CIRCUIT BOOSTER
NL: TURN-OFF BUFFER
DESAT > 10.3-10.9 V (above the 10.0 V maximum trip of the -Q1 grade) -> MMBT3904 -> MMBT3906 charges BG to VEE + 10 V; per device AO3400A + 22R pull the gate to VEE; BG holds ~3 us (1k + FET gates).
NL: MILLER CLAMP CONTROL
Gate and Kelvin of each device as coupled pairs of equal length from the COM star; Ron, Roff, Kelvin R, 10k + 1n, Zeners and the clamp FET + C_VL at each device (loop <= 1 nH). PNP followers next to their three gates. DESAT string >= 2.5 mm pad gap per diode; coat to PD1. Miller hold of six gates N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
MMBT3906 inverter (E COM, base BAT54+2.2k on CLAMP) drives CG to COM once the lowest gate is below ~-1.2 V; MMBT3904 release (from OUTH via 5.6 V Zener) holds CG at VEE while OUTH drives.
Per device: Ron/Roff, 0.5R Kelvin R to the COM star, 10k and Zeners (about +21 V / -5.7 V) on its own Kelvin net. Miller hold: N-MOSFET clamp (PMV30ENEA) gate-pin to a local VEE (1u on the Kelvin pin). LAYOUT: FET + 1u at the device, loop <= 1 nH.
LEG N: LAYOUT RULES
DESAT pin (internal 500 uA blanking source, trip 8.5-10.0 V) - Rs - 2 x BYG23T-M3/TR (1300 V each) - drain. BAT54S keeps DX between COM and VDD against dv/dt through the string; Cblk footprint DNP.
NL: LOGIC SIDE
SN6505B push-pull 420 kHz from +5V, BIAS_EN high = on; T_BIAS4 custom, functional insulation (PD-free >= 1.75 kVpk, <= 5 pF per secondary). Per channel: bridge, PNP regulator VDD-VEE, ATL431 COM split.
