vectivolt/PCM/hardware/PCS-PWR-4W/sheets/15_filta.kicad_sch

## KiCad design hardware/PCS-PWR-4W/sheets/15_filta.kicad_sch (2026-10-06)

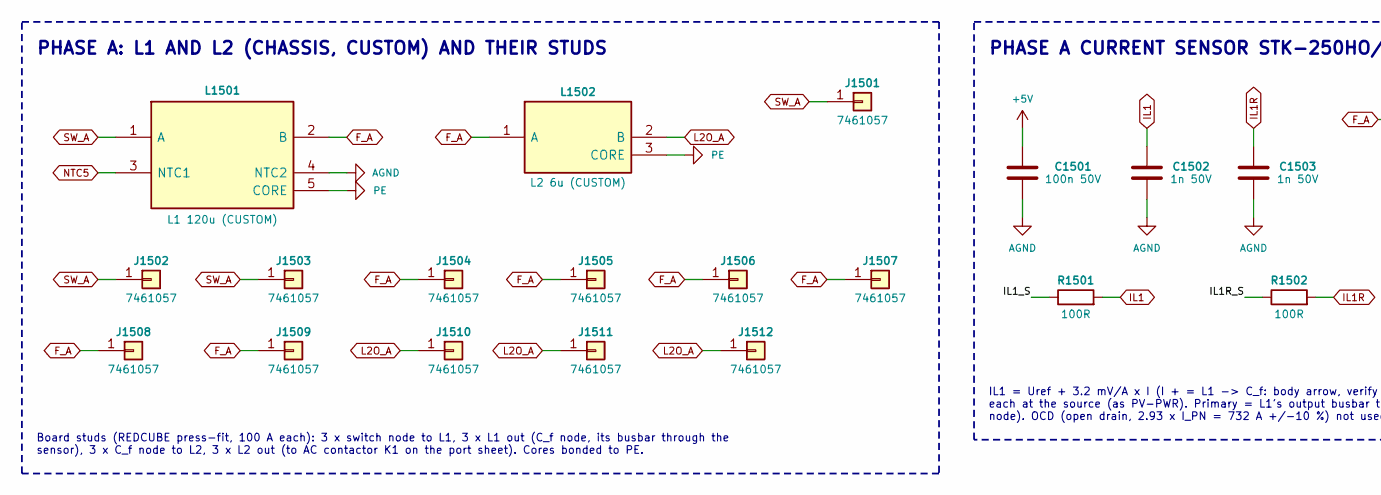
[picture p327: schematic 15_filta.kicad_sch, part in row 1, column 1]

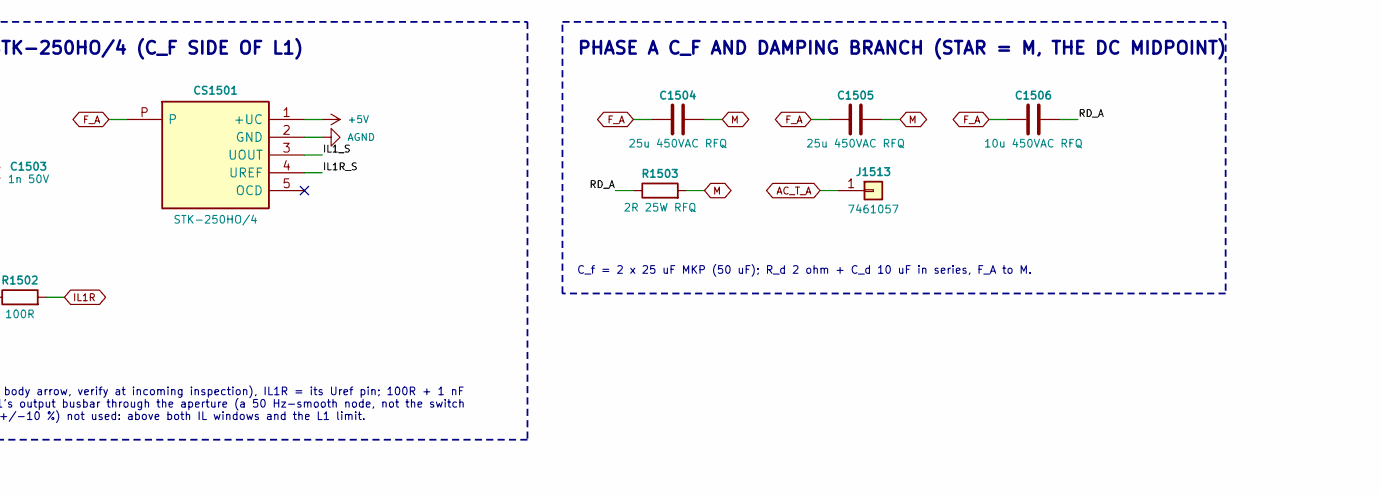
[picture p328: schematic 15_filta.kicad_sch, part in row 1, column 2]

Parts:
C1501: 100n 50V
C1502, C1503: 1n 50V
C1504, C1505: 25u 450VAC RFQ
C1506: 10u 450VAC RFQ
CS1501: STK-250HO/4; MPN STK-250HO/4
J1501, J1502, J1503, J1504, J1505, J1506, J1507, J1508, J1509, J1510, J1511, J1512, J1513: 7461057; MPN 7461057
L1501: L1 120u (CUSTOM)
L1502: L2 6u (CUSTOM)
R1501, R1502: 100R
R1503: 2R 25W RFQ

Connections:
+5V: C1501.1, CS1501.1 (+UC)
AC_T_A: J1513.1
AGND: C1501.2, C1502.2, C1503.2, CS1501.2 (GND), L1501.4 (NTC2)
F_A: C1504.1, C1505.1, C1506.1, CS1501.P, J1504.1, J1505.1, J1506.1, J1507.1, J1508.1, J1509.1, L1501.2 (B), L1502.1 (A)
IL1: C1502.1, R1501.2
IL1R: C1503.1, R1502.2
IL1R_S: CS1501.4 (UREF), R1502.1
IL1_S: CS1501.3 (UOUT), R1501.1
L2O_A: J1510.1, J1511.1, J1512.1, L1502.2 (B)
M: C1504.2, C1505.2, R1503.2
NTC5: L1501.3 (NTC1)
PE: L1501.5 (CORE), L1502.3 (CORE)
RD_A: C1506.2, R1503.1
SW_A: J1501.1, J1502.1, J1503.1, L1501.1 (A)

Notes on the sheet:
C_f = 2 x 25 uF MKP (50 uF); R_d 2 ohm + C_d 10 uF in series, F_A to M.
PHASE A C_F AND DAMPING BRANCH (STAR = M, THE DC MIDPOINT)
Board studs (REDCUBE press-fit, 100 A each): 3 x switch node to L1, 3 x L1 out (C_f node, its busbar through the sensor), 3 x C_f node to L2, 3 x L2 out (to AC contactor K1 on the port sheet). Cores bonded to PE.
PHASE A CURRENT SENSOR STK-250HO/4 (C_F SIDE OF L1)
IL1 = Uref + 3.2 mV/A x I (I + = L1 -> C_f: body arrow, verify at incoming inspection), IL1R = its Uref pin; 100R + 1 nF each at the source (as PV-PWR). Primary = L1's output busbar through the aperture (a 50 Hz-smooth node, not the switch node). OCD (open drain, 2.93 x I_PN = 732 A +/-10 %) not us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
PHASE A: L1 AND L2 (CHASSIS, CUSTOM) AND THEIR STUDS
