vectivolt/PCM/hardware/PCS-PWR-4W/sheets/16_filtb.kicad_sch

## KiCad design hardware/PCS-PWR-4W/sheets/16_filtb.kicad_sch (2026-10-06)

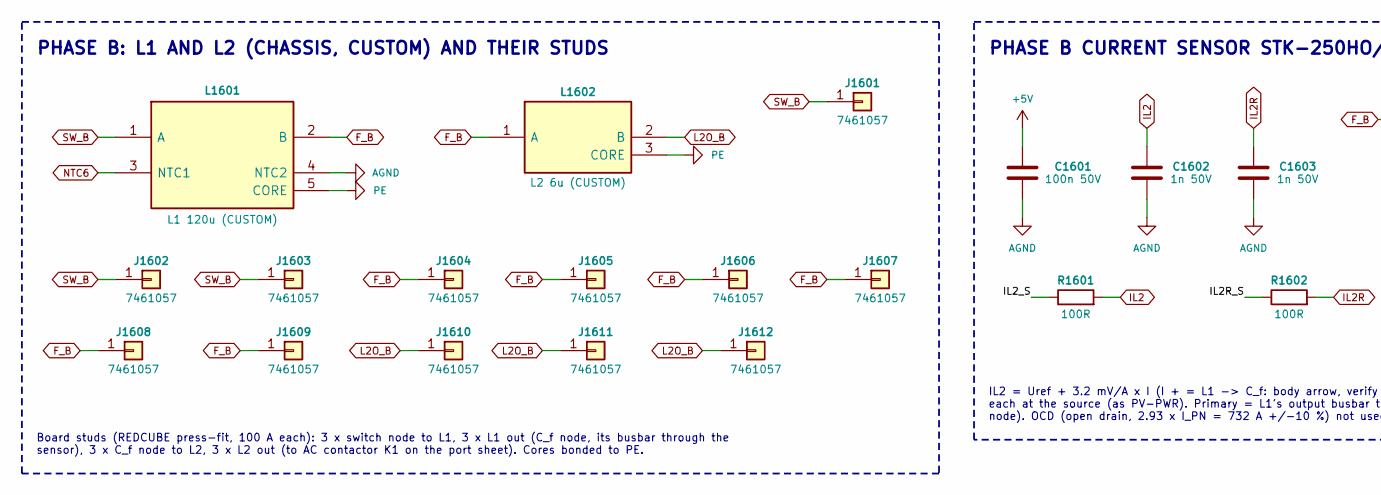
[picture p329: schematic 16_filtb.kicad_sch, part in row 1, column 1]

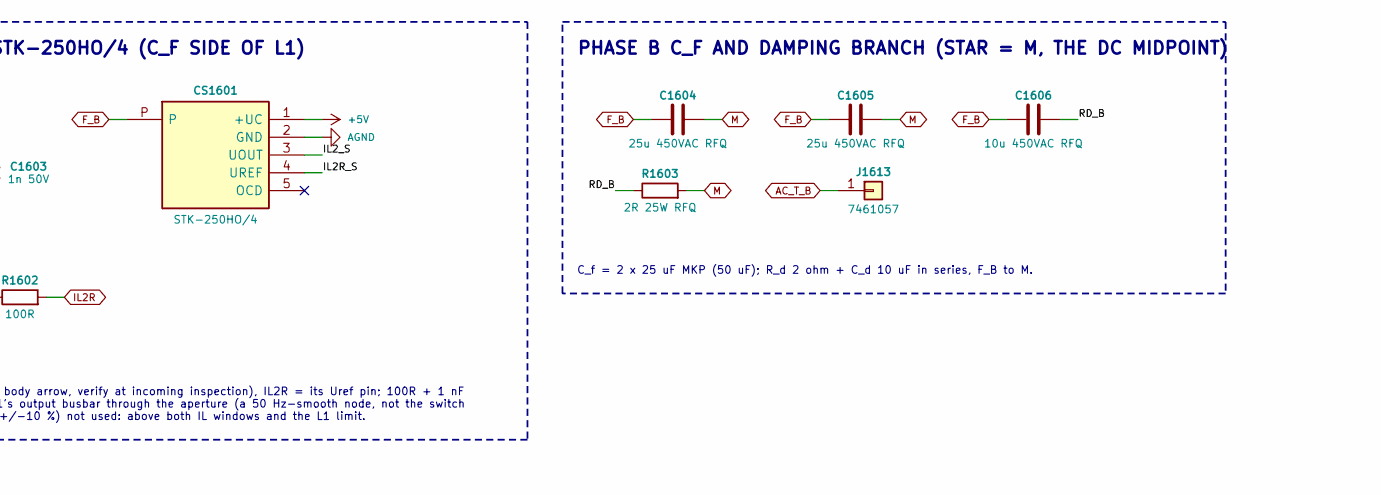
[picture p330: schematic 16_filtb.kicad_sch, part in row 1, column 2]

Parts:
C1601: 100n 50V
C1602, C1603: 1n 50V
C1604, C1605: 25u 450VAC RFQ
C1606: 10u 450VAC RFQ
CS1601: STK-250HO/4; MPN STK-250HO/4
J1601, J1602, J1603, J1604, J1605, J1606, J1607, J1608, J1609, J1610, J1611, J1612, J1613: 7461057; MPN 7461057
L1601: L1 120u (CUSTOM)
L1602: L2 6u (CUSTOM)
R1601, R1602: 100R
R1603: 2R 25W RFQ

Connections:
+5V: C1601.1, CS1601.1 (+UC)
AC_T_B: J1613.1
AGND: C1601.2, C1602.2, C1603.2, CS1601.2 (GND), L1601.4 (NTC2)
F_B: C1604.1, C1605.1, C1606.1, CS1601.P, J1604.1, J1605.1, J1606.1, J1607.1, J1608.1, J1609.1, L1601.2 (B), L1602.1 (A)
IL2: C1602.1, R1601.2
IL2R: C1603.1, R1602.2
IL2R_S: CS1601.4 (UREF), R1602.1
IL2_S: CS1601.3 (UOUT), R1601.1
L2O_B: J1610.1, J1611.1, J1612.1, L1602.2 (B)
M: C1604.2, C1605.2, R1603.2
NTC6: L1601.3 (NTC1)
PE: L1601.5 (CORE), L1602.3 (CORE)
RD_B: C1606.2, R1603.1
SW_B: J1601.1, J1602.1, J1603.1, L1601.1 (A)

Notes on the sheet:
PHASE B CURRENT SENSOR STK-250HO/4 (C_F SIDE OF L1)
IL2 = Uref + 3.2 mV/A x I (I + = L1 -> C_f: body arrow, verify at incoming inspection), IL2R = its Uref pin; 100R + 1 nF each at the source (as PV-PWR). Primary = L1's output busbar through the aperture (a 50 Hz-smooth node, not the switch node). OCD (open drain, 2.93 x I_PN = 732 A +/-10 %) not us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
PHASE B: L1 AND L2 (CHASSIS, CUSTOM) AND THEIR STUDS
Board studs (REDCUBE press-fit, 100 A each): 3 x switch node to L1, 3 x L1 out (C_f node, its busbar through the sensor), 3 x C_f node to L2, 3 x L2 out (to AC contactor K1 on the port sheet). Cores bonded to PE.
C_f = 2 x 25 uF MKP (50 uF); R_d 2 ohm + C_d 10 uF in series, F_B to M.
PHASE B C_F AND DAMPING BRANCH (STAR = M, THE DC MIDPOINT)
