vectivolt/PCM/hardware/PCS-PWR-4W/sheets/17_filtc.kicad_sch

## KiCad design hardware/PCS-PWR-4W/sheets/17_filtc.kicad_sch (2026-10-06)

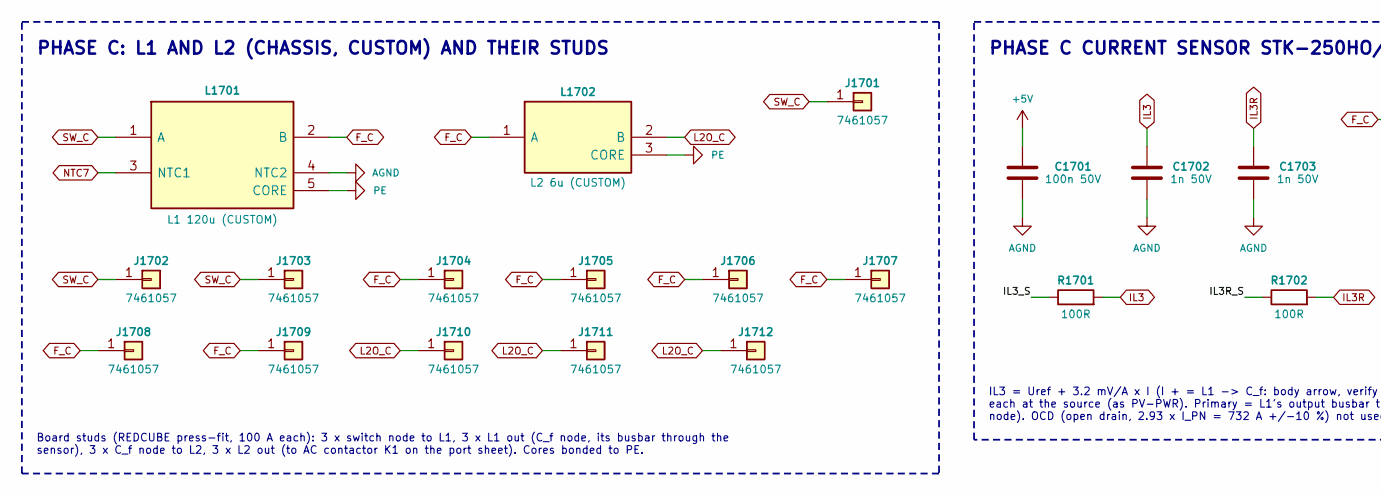
[picture p331: schematic 17_filtc.kicad_sch, part in row 1, column 1]

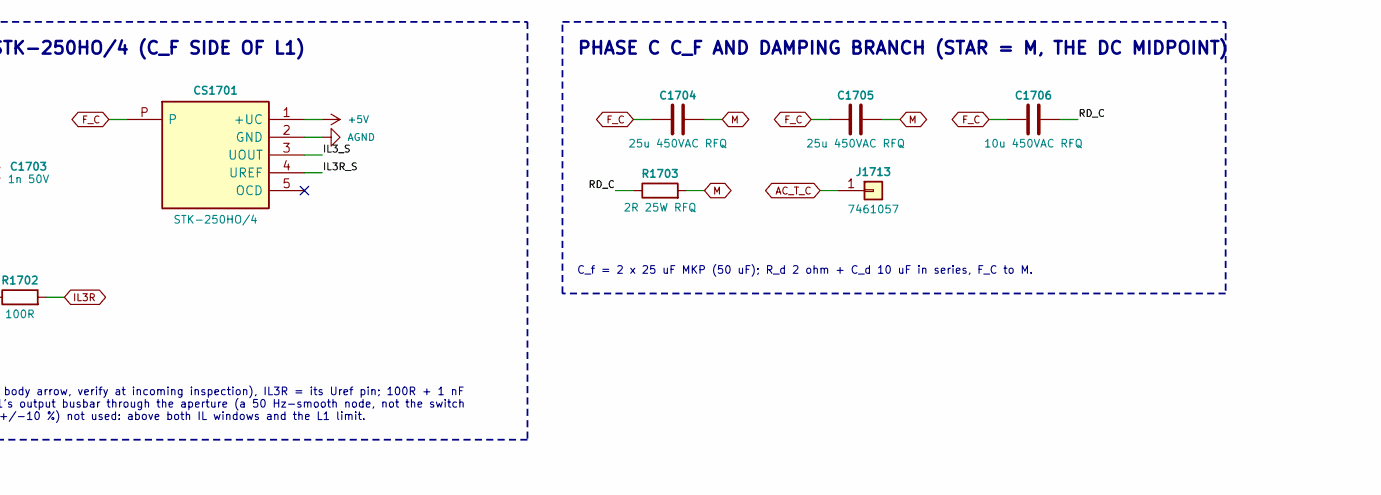
[picture p332: schematic 17_filtc.kicad_sch, part in row 1, column 2]

Parts:
C1701: 100n 50V
C1702, C1703: 1n 50V
C1704, C1705: 25u 450VAC RFQ
C1706: 10u 450VAC RFQ
CS1701: STK-250HO/4; MPN STK-250HO/4
J1701, J1702, J1703, J1704, J1705, J1706, J1707, J1708, J1709, J1710, J1711, J1712, J1713: 7461057; MPN 7461057
L1701: L1 120u (CUSTOM)
L1702: L2 6u (CUSTOM)
R1701, R1702: 100R
R1703: 2R 25W RFQ

Connections:
+5V: C1701.1, CS1701.1 (+UC)
AC_T_C: J1713.1
AGND: C1701.2, C1702.2, C1703.2, CS1701.2 (GND), L1701.4 (NTC2)
F_C: C1704.1, C1705.1, C1706.1, CS1701.P, J1704.1, J1705.1, J1706.1, J1707.1, J1708.1, J1709.1, L1701.2 (B), L1702.1 (A)
IL3: C1702.1, R1701.2
IL3R: C1703.1, R1702.2
IL3R_S: CS1701.4 (UREF), R1702.1
IL3_S: CS1701.3 (UOUT), R1701.1
L2O_C: J1710.1, J1711.1, J1712.1, L1702.2 (B)
M: C1704.2, C1705.2, R1703.2
NTC7: L1701.3 (NTC1)
PE: L1701.5 (CORE), L1702.3 (CORE)
RD_C: C1706.2, R1703.1
SW_C: J1701.1, J1702.1, J1703.1, L1701.1 (A)

Notes on the sheet:
PHASE C: L1 AND L2 (CHASSIS, CUSTOM) AND THEIR STUDS
PHASE C C_F AND DAMPING BRANCH (STAR = M, THE DC MIDPOINT)
PHASE C CURRENT SENSOR STK-250HO/4 (C_F SIDE OF L1)
C_f = 2 x 25 uF MKP (50 uF); R_d 2 ohm + C_d 10 uF in series, F_C to M.
Board studs (REDCUBE press-fit, 100 A each): 3 x switch node to L1, 3 x L1 out (C_f node, its busbar through the sensor), 3 x C_f node to L2, 3 x L2 out (to AC contactor K1 on the port sheet). Cores bonded to PE.
IL3 = Uref + 3.2 mV/A x I (I + = L1 -> C_f: body arrow, verify at incoming inspection), IL3R = its Uref pin; 100R + 1 nF each at the source (as PV-PWR). Primary = L1's output busbar through the aperture (a 50 Hz-smooth node, not the switch node). OCD (open drain, 2.93 x I_PN = 732 A +/-10 %) not us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
