vectivolt/PCM/hardware/PCS-PWR-4W/sheets/18_filtn.kicad_sch

## KiCad design hardware/PCS-PWR-4W/sheets/18_filtn.kicad_sch (2026-10-06)

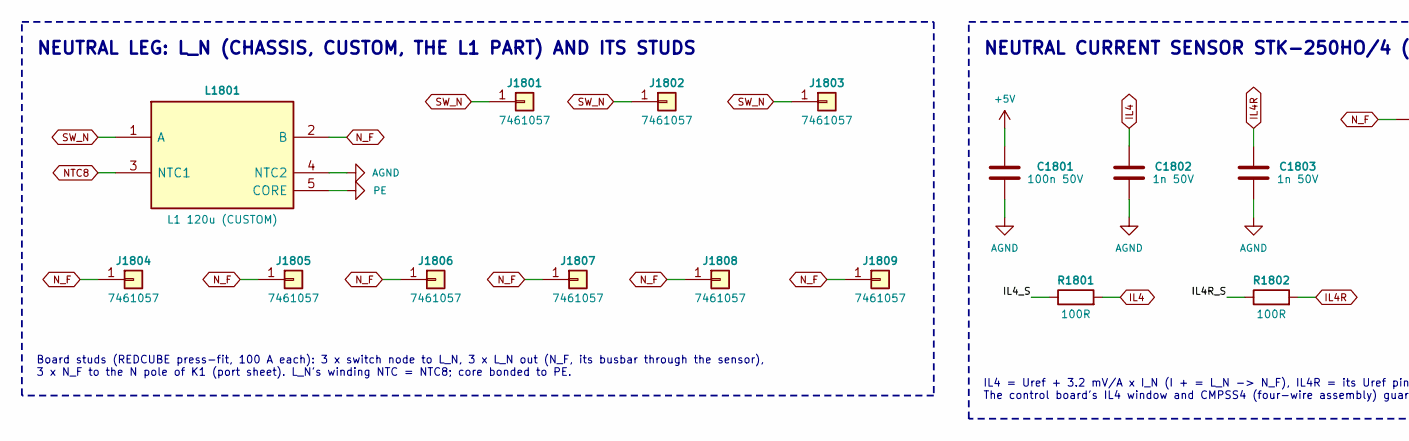
[picture p333: schematic 18_filtn.kicad_sch, part in row 1, column 1]

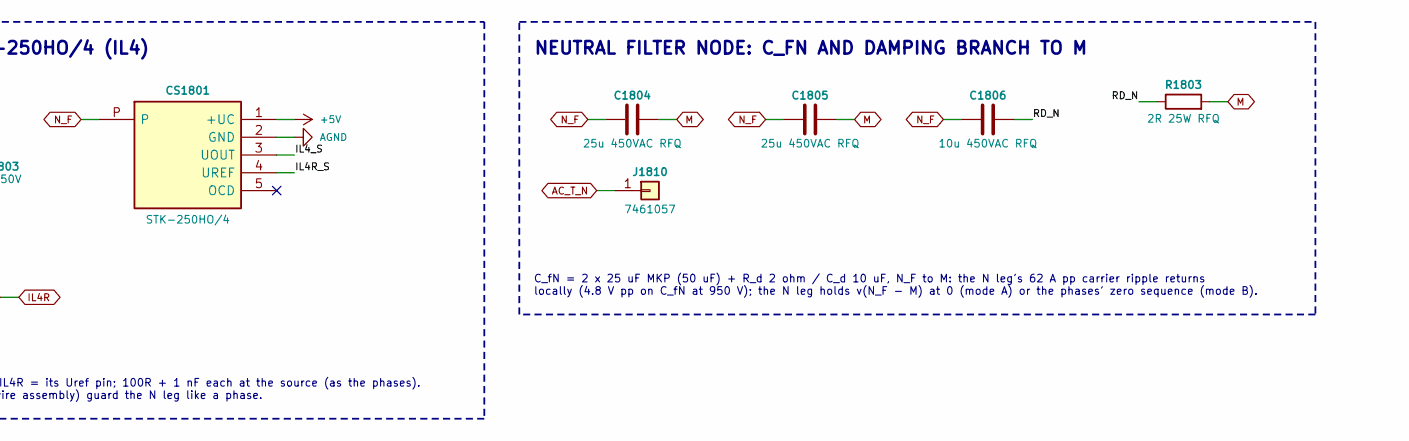
[picture p334: schematic 18_filtn.kicad_sch, part in row 1, column 2]

Parts:
C1801: 100n 50V
C1802, C1803: 1n 50V
C1804, C1805: 25u 450VAC RFQ
C1806: 10u 450VAC RFQ
CS1801: STK-250HO/4; MPN STK-250HO/4
J1801, J1802, J1803, J1804, J1805, J1806, J1807, J1808, J1809, J1810: 7461057; MPN 7461057
L1801: L1 120u (CUSTOM)
R1801, R1802: 100R
R1803: 2R 25W RFQ

Connections:
+5V: C1801.1, CS1801.1 (+UC)
AC_T_N: J1810.1
AGND: C1801.2, C1802.2, C1803.2, CS1801.2 (GND), L1801.4 (NTC2)
IL4: C1802.1, R1801.2
IL4R: C1803.1, R1802.2
IL4R_S: CS1801.4 (UREF), R1802.1
IL4_S: CS1801.3 (UOUT), R1801.1
M: C1804.2, C1805.2, R1803.2
NTC8: L1801.3 (NTC1)
N_F: C1804.1, C1805.1, C1806.1, CS1801.P, J1804.1, J1805.1, J1806.1, J1807.1, J1808.1, J1809.1, L1801.2 (B)
PE: L1801.5 (CORE)
RD_N: C1806.2, R1803.1
SW_N: J1801.1, J1802.1, J1803.1, L1801.1 (A)

Notes on the sheet:
NEUTRAL CURRENT SENSOR STK-250HO/4 (IL4)
NEUTRAL LEG: L_N (CHASSIS, CUSTOM, THE L1 PART) AND ITS STUDS
C_fN = 2 x 25 uF MKP (50 uF) + R_d 2 ohm / C_d 10 uF, N_F to M: the N leg's 62 A pp carrier ripple returns locally (4.8 V pp on C_fN at 950 V); the N leg holds v(N_F - M) at 0 (mode A) or the phases' zero sequence (mode B).
NEUTRAL FILTER NODE: C_FN AND DAMPING BRANCH TO M
IL4 = Uref + 3.2 mV/A x I_N (I + = L_N -> N_F), IL4R = its Uref pin; 100R + 1 nF each at the source (as the phases). The control board's IL4 window and CMPSS4 (four-wire assembly) guard the N leg like a phase.
Board studs (REDCUBE press-fit, 100 A each): 3 x switch node to L_N, 3 x L_N out (N_F, its busbar through the sensor), 3 x N_F to the N pole of K1 (port sheet). L_N's winding NTC = NTC8; core bonded to PE.
