vectivolt/PCM/hardware/PCS-PWR-4W/sheets/19_acsense.kicad_sch

## KiCad design hardware/PCS-PWR-4W/sheets/19_acsense.kicad_sch (2026-10-06)

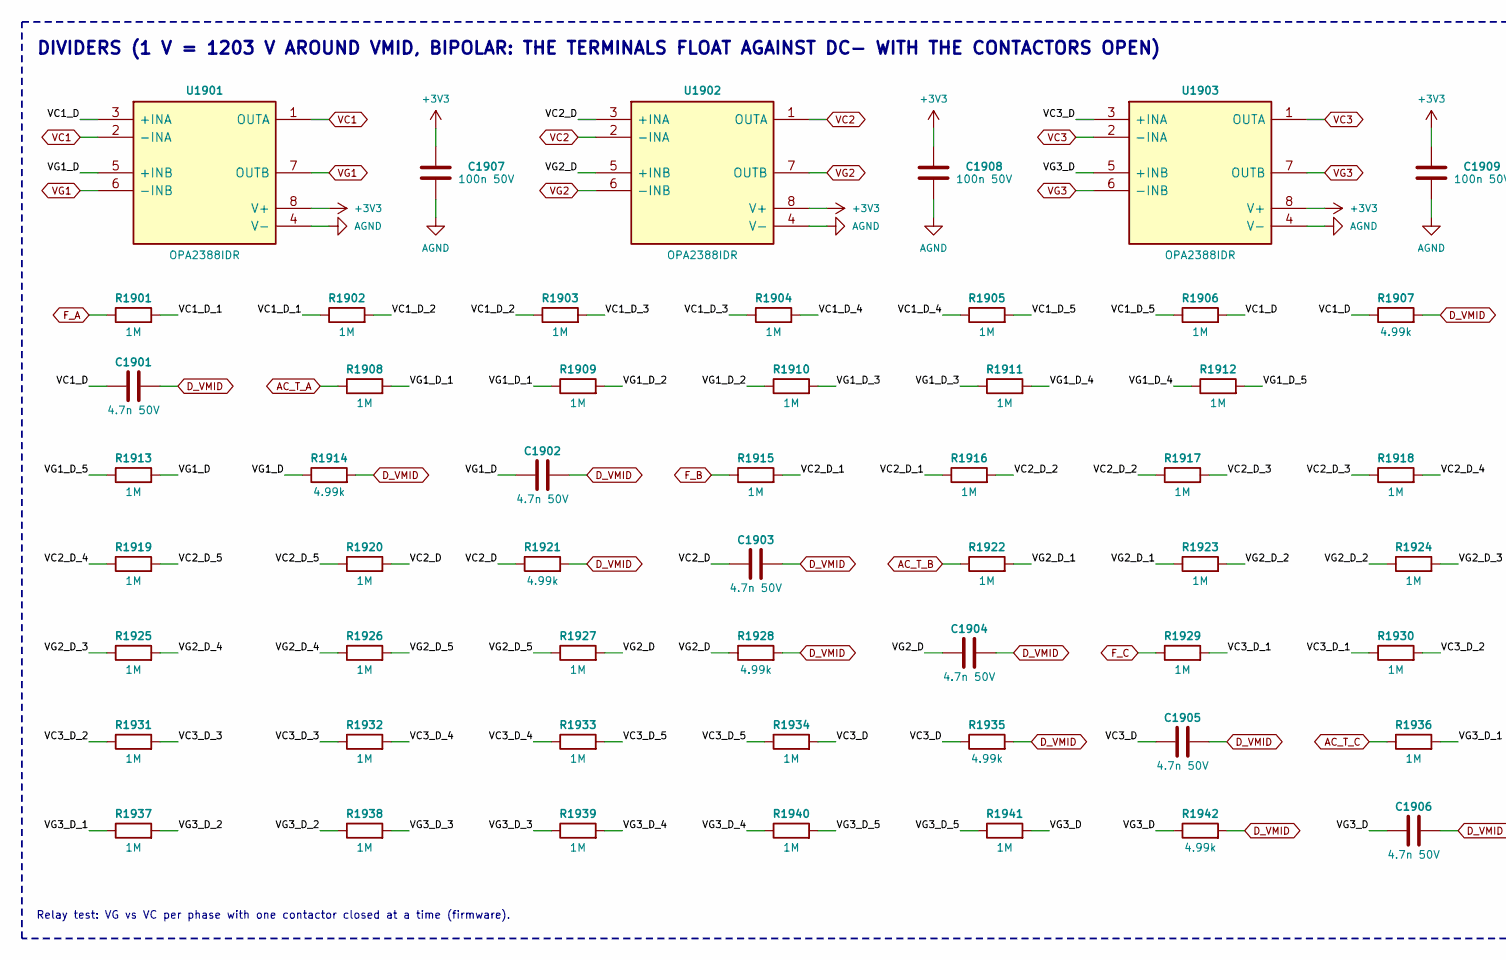
[picture p335: schematic 19_acsense.kicad_sch, part in row 1, column 1]

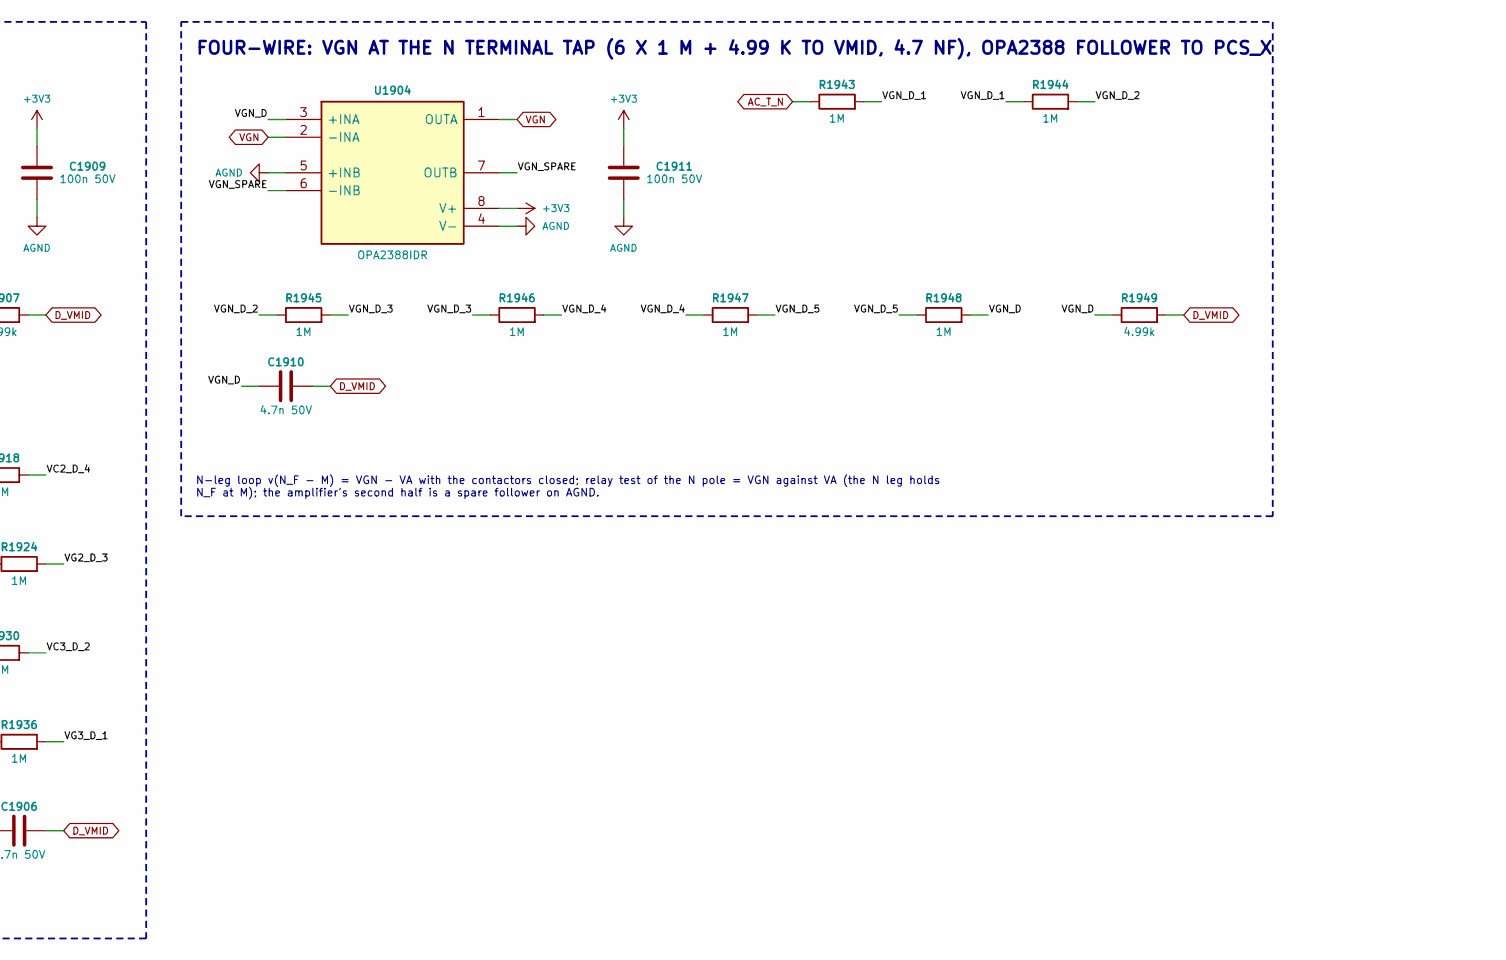
[picture p336: schematic 19_acsense.kicad_sch, part in row 1, column 2]

Parts:
C1901, C1902, C1903, C1904, C1905, C1906, C1910: 4.7n 50V
C1907, C1908, C1909, C1911: 100n 50V
R1901, R1902, R1903, R1904, R1905, R1906, R1908, R1909, R1910, R1911, R1912, R1913, R1915, R1916, R1917, R1918, R1919, R1920, R1922, R1923, R1924, R1925, R1926, R1927, R1929, R1930, R1931, R1932, R1933, R1934, R1936, R1937, R1938, R1939, R1940, R1941, R1943, R1944, R1945, R1946, R1947, R1948: 1M; MPN ARHV06BTC1004A
R1907, R1914, R1921, R1928, R1935, R1942, R1949: 4.99k; MPN TNPW12064K99BEEA
U1901, U1902, U1903, U1904: OPA2388IDR; MPN OPA2388IDR

Connections:
+3V3: C1907.1, C1908.1, C1909.1, C1911.1, U1901.8 (V+), U1902.8 (V+), U1903.8 (V+), U1904.8 (V+)
AC_T_A: R1908.1
AC_T_B: R1922.1
AC_T_C: R1936.1
AC_T_N: R1943.1
AGND: C1907.2, C1908.2, C1909.2, C1911.2, U1901.4 (V-), U1902.4 (V-), U1903.4 (V-), U1904.4 (V-), U1904.5 (+INB)
D_VMID: C1901.2, C1902.2, C1903.2, C1904.2, C1905.2, C1906.2, C1910.2, R1907.2, R1914.2, R1921.2, R1928.2, R1935.2, R1942.2, R1949.2
F_A: R1901.1
F_B: R1915.1
F_C: R1929.1
VC1: U1901.1 (OUTA), U1901.2 (-INA)
VC1_D: C1901.1, R1906.2, R1907.1, U1901.3 (+INA)
VC1_D_1: R1901.2, R1902.1
VC1_D_2: R1902.2, R1903.1
VC1_D_3: R1903.2, R1904.1
VC1_D_4: R1904.2, R1905.1
VC1_D_5: R1905.2, R1906.1
VC2: U1902.1 (OUTA), U1902.2 (-INA)
VC2_D: C1903.1, R1920.2, R1921.1, U1902.3 (+INA)
VC2_D_1: R1915.2, R1916.1
VC2_D_2: R1916.2, R1917.1
VC2_D_3: R1917.2, R1918.1
VC2_D_4: R1918.2, R1919.1
VC2_D_5: R1919.2, R1920.1
VC3: U1903.1 (OUTA), U1903.2 (-INA)
VC3_D: C1905.1, R1934.2, R1935.1, U1903.3 (+INA)
VC3_D_1: R1929.2, R1930.1
VC3_D_2: R1930.2, R1931.1
VC3_D_3: R1931.2, R1932.1
VC3_D_4: R1932.2, R1933.1
VC3_D_5: R1933.2, R1934.1
VG1: U1901.6 (-INB), U1901.7 (OUTB)
VG1_D: C1902.1, R1913.2, R1914.1, U1901.5 (+INB)
VG1_D_1: R1908.2, R1909.1
VG1_D_2: R1909.2, R1910.1
VG1_D_3: R1910.2, R1911.1
VG1_D_4: R1911.2, R1912.1
VG1_D_5: R1912.2, R1913.1
VG2: U1902.6 (-INB), U1902.7 (OUTB)
VG2_D: C1904.1, R1927.2, R1928.1, U1902.5 (+INB)
VG2_D_1: R1922.2, R1923.1
VG2_D_2: R1923.2, R1924.1
VG2_D_3: R1924.2, R1925.1
VG2_D_4: R1925.2, R1926.1
VG2_D_5: R1926.2, R1927.1
VG3: U1903.6 (-INB), U1903.7 (OUTB)
VG3_D: C1906.1, R1941.2, R1942.1, U1903.5 (+INB)
VG3_D_1: R1936.2, R1937.1
VG3_D_2: R1937.2, R1938.1
VG3_D_3: R1938.2, R1939.1
VG3_D_4: R1939.2, R1940.1
VG3_D_5: R1940.2, R1941.1
VGN: U1904.1 (OUTA), U1904.2 (-INA)
VGN_D: C1910.1, R1948.2, R1949.1, U1904.3 (+INA)
VGN_D_1: R1943.2, R1944.1
VGN_D_2: R1944.2, R1945.1
VGN_D_3: R1945.2, R1946.1
VGN_D_4: R1946.2, R1947.1
VGN_D_5: R1947.2, R1948.1
VGN_SPARE: U1904.6 (-INB), U1904.7 (OUTB)

Notes on the sheet:
Relay test: VG vs VC per phase with one contactor closed at a time (firmware).
DIVIDERS (1 V = 1203 V AROUND VMID, BIPOLAR: THE TERMINALS FLOAT AGAINST DC- WITH THE CONTACTORS OPEN)
FOUR-WIRE: VGN AT THE N TERMINAL TAP (6 X 1 M + 4.99 K TO VMID, 4.7 NF), OPA2388 FOLLOWER TO PCS_X
N-leg loop v(N_F - M) = VGN - VA with the contactors closed; relay test of the N pole = VGN against VA (the N leg holds N_F at M); the amplifier's second half is a spare follower on AGND.
