vectivolt/PCM/hardware/PCS-PWR-4W/sheets/20_leanB_power.kicad_sch

## KiCad design hardware/PCS-PWR-4W/sheets/20_leanB_power.kicad_sch (2026-10-06)

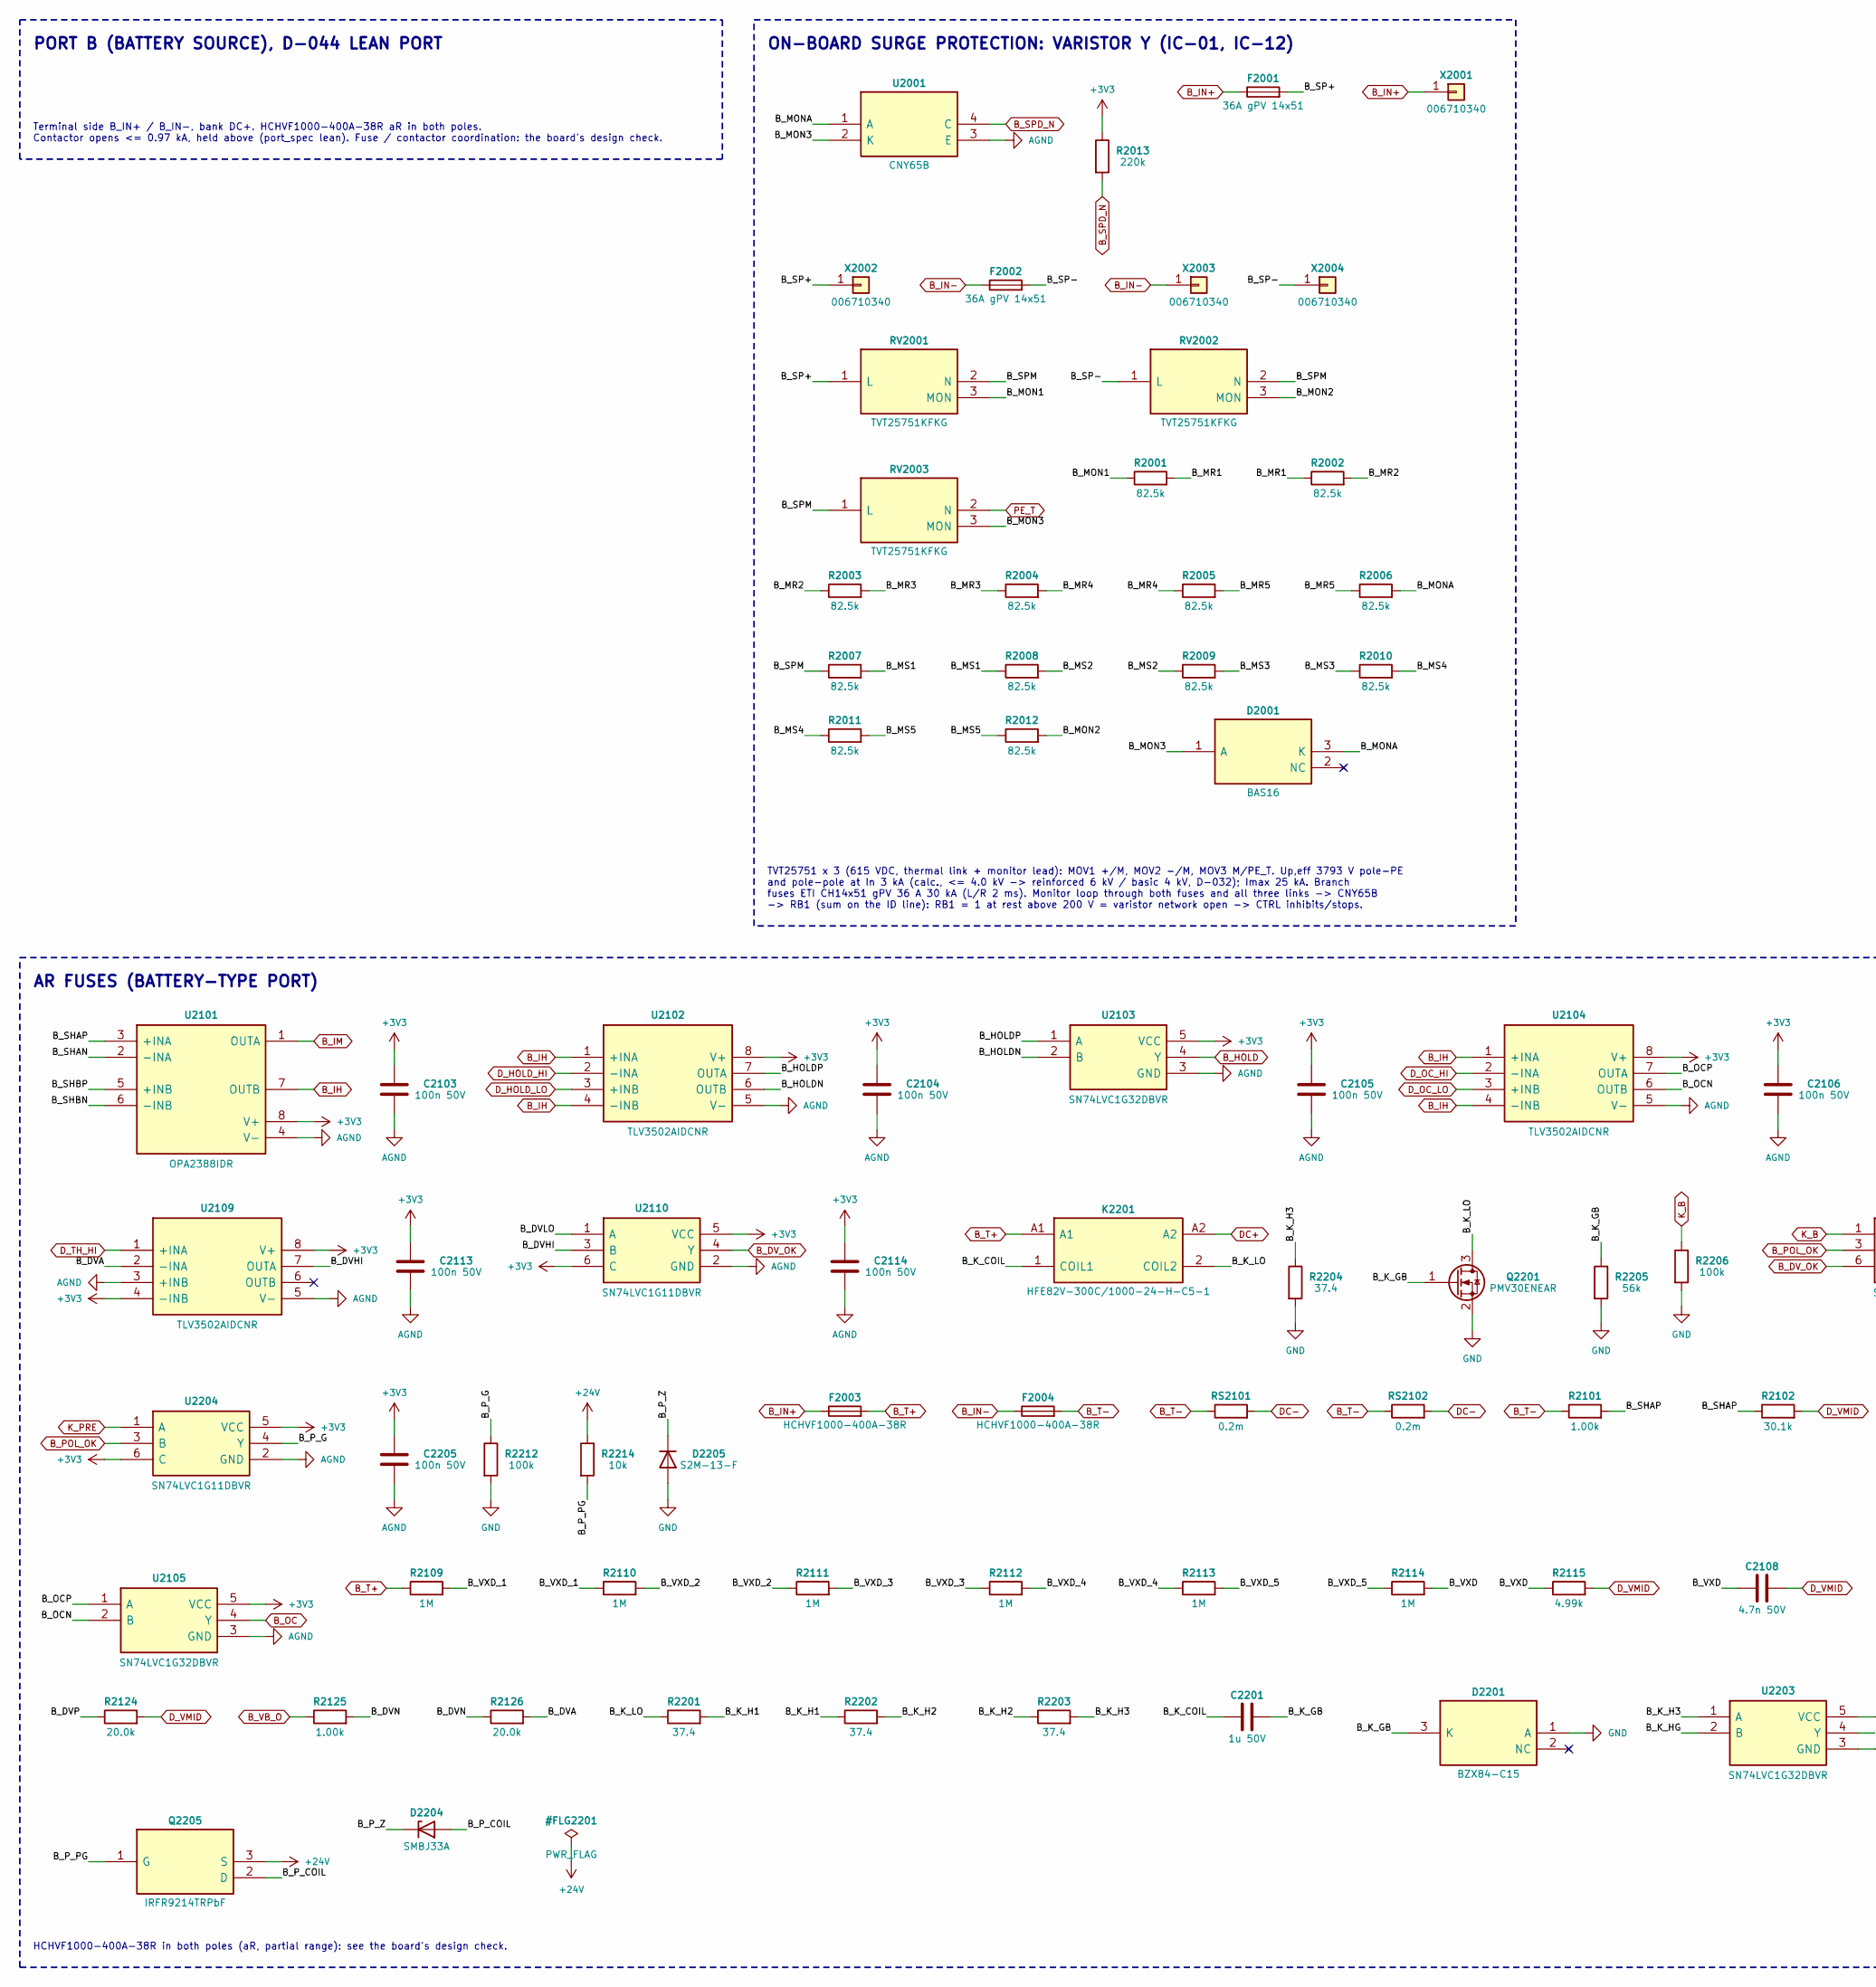
[picture p337: schematic 20_leanB_power.kicad_sch, part in row 1, column 1]

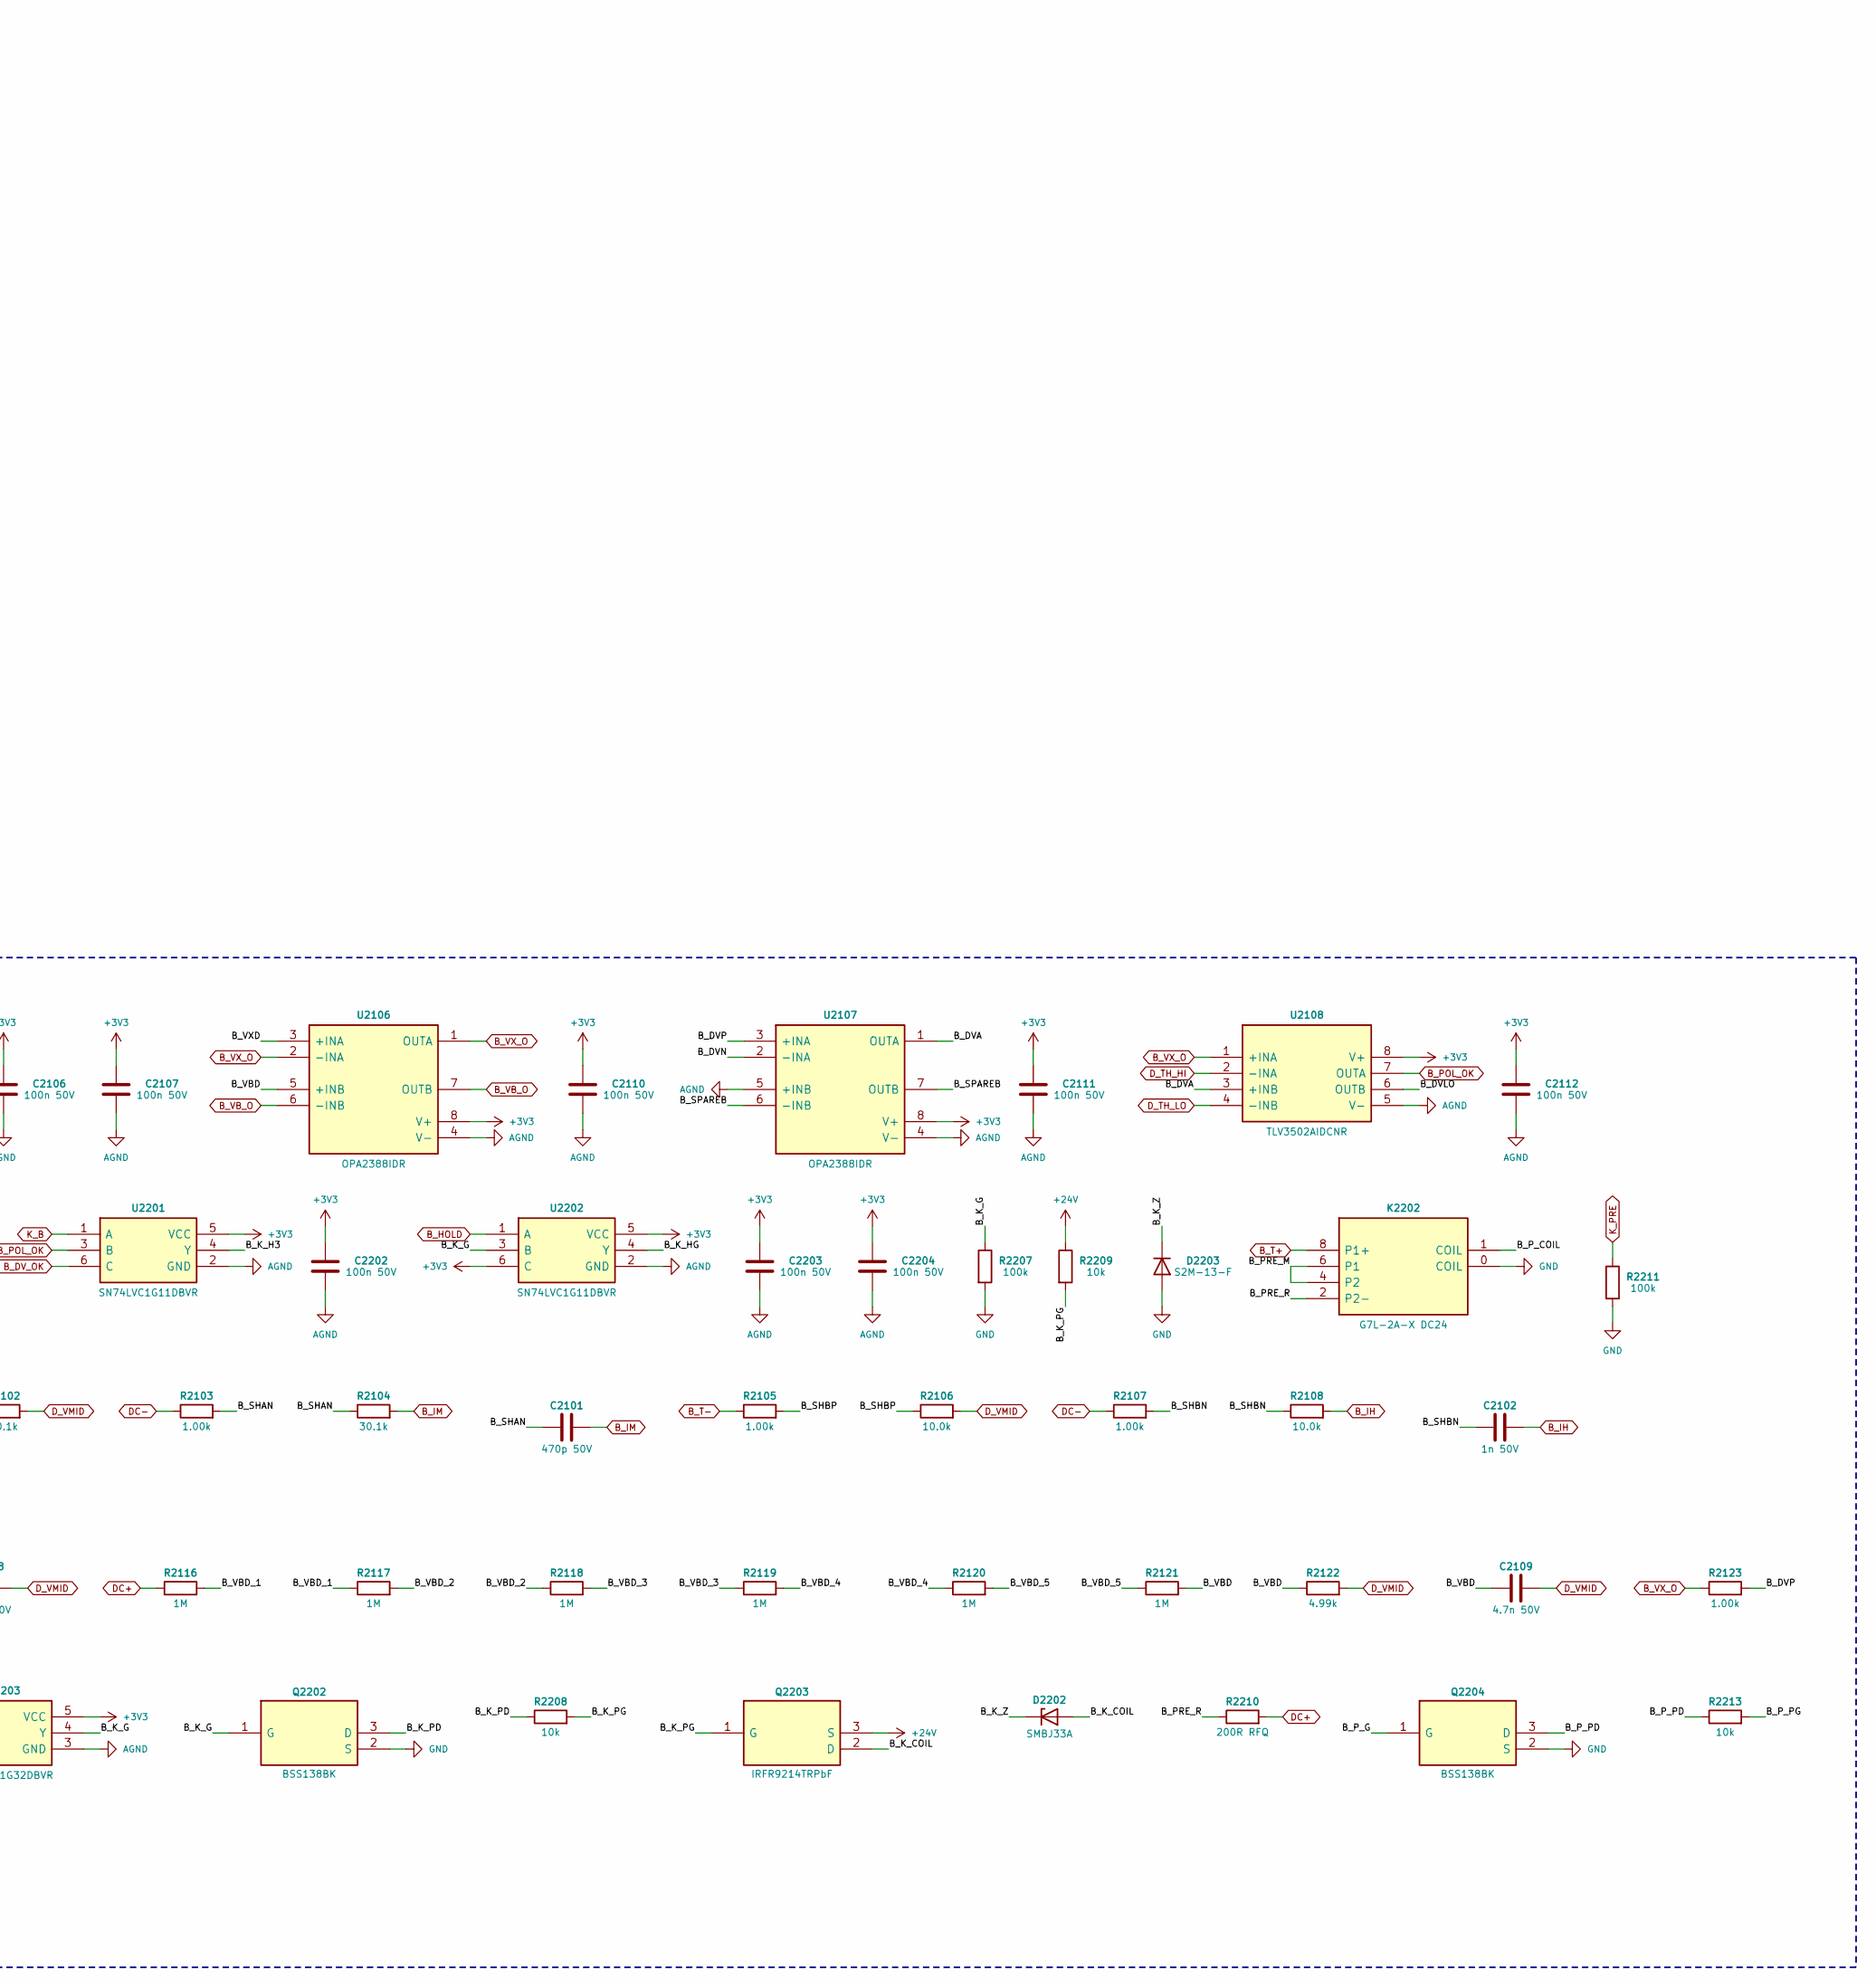
[picture p338: schematic 20_leanB_power.kicad_sch, part in row 1, column 2]

Parts:
C2101: 470p 50V
C2102: 1n 50V
C2103, C2104, C2105, C2106, C2107, C2110, C2111, C2112, C2113, C2114, C2202, C2203, C2204, C2205: 100n 50V
C2108, C2109: 4.7n 50V
C2201: 1u 50V
D2001: BAS16; MPN BAS16
D2201: BZX84-C15; MPN BZX84-C15
D2202, D2204: SMBJ33A; MPN SMBJ33A
D2203, D2205: S2M-13-F; MPN S2M-13-F
F2001, F2002: 36A gPV 14x51; MPN 002637115
F2003, F2004: HCHVF1000-400A-38R; MPN HCHVF1000-400A-38R
K2201: HFE82V-300C/1000-24-H-C5-1; MPN HFE82V-300C/1000-24-H-C5-1
K2202: G7L-2A-X DC24; MPN G7L-2A-X DC24
Q2201: PMV30ENEAR; MPN PMV30ENEAR
Q2202, Q2204: BSS138BK; MPN BSS138BK
Q2203, Q2205: IRFR9214TRPbF; MPN IRFR9214TRPbF
R2001, R2002, R2003, R2004, R2005, R2006, R2007, R2008, R2009, R2010, R2011, R2012: 82.5k
R2013: 220k
R2101, R2103, R2105, R2107, R2123, R2125: 1.00k
R2102, R2104: 30.1k
R2106, R2108: 10.0k
R2109, R2110, R2111, R2112, R2113, R2114, R2116, R2117, R2118, R2119, R2120, R2121: 1M; MPN ARHV06BTC1004A
R2115, R2122: 4.99k; MPN TNPW12064K99BEEA
R2124, R2126: 20.0k
R2201, R2202, R2203, R2204: 37.4
R2205: 56k
R2206, R2207, R2211, R2212: 100k
R2208, R2209, R2213, R2214: 10k
R2210: 200R RFQ
RS2101, RS2102: 0.2m; MPN CSS2H-3920R-L200F
RV2001, RV2002, RV2003: TVT25751KFKG; MPN TVT25751KFKG
U2001: CNY65B; MPN CNY65B
U2101, U2106, U2107: OPA2388IDR; MPN OPA2388IDR
U2102, U2104, U2108, U2109: TLV3502AIDCNR; MPN TLV3502AIDCNR
U2103, U2105, U2203: SN74LVC1G32DBVR; MPN SN74LVC1G32DBVR
U2110, U2201, U2202, U2204: SN74LVC1G11DBVR; MPN SN74LVC1G11DBVR
X2001, X2002, X2003, X2004: 006710340; MPN 006710340

Connections:
+3V3: C2103.1, C2104.1, C2105.1, C2106.1, C2107.1, C2110.1, C2111.1, C2112.1, C2113.1, C2114.1, C2202.1, C2203.1, C2204.1, C2205.1, R2013.1, U2101.8 (V+), U2102.8 (V+), U2103.5 (VCC), U2104.8 (V+), U2105.5 (VCC), U2106.8 (V+), U2107.8 (V+), U2108.8 (V+), U2109.4 (-INB), U2109.8 (V+), U2110.5 (VCC), U2110.6 (C), U2201.5 (VCC), U2202.5 (VCC), U2202.6 (C), U2203.5 (VCC), U2204.5 (VCC), U2204.6 (C)
+24V: Q2203.3 (S), Q2205.3 (S), R2209.1, R2214.1
AGND: C2103.2, C2104.2, C2105.2, C2106.2, C2107.2, C2110.2, C2111.2, C2112.2, C2113.2, C2114.2, C2202.2, C2203.2, C2204.2, C2205.2, U2001.3 (E), U2101.4 (V-), U2102.5 (V-), U2103.3 (GND), U2104.5 (V-), U2105.3 (GND), U2106.4 (V-), U2107.4 (V-), U2107.5 (+INB), U2108.5 (V-), U2109.3 (+INB), U2109.5 (V-), U2110.2 (GND), U2201.2 (GND), U2202.2 (GND), U2203.3 (GND), U2204.2 (GND)
B_DVA: R2126.2, U2107.1 (OUTA), U2108.3 (+INB), U2109.2 (-INA)
B_DVHI: U2109.7 (OUTA), U2110.3 (B)
B_DVLO: U2108.6 (OUTB), U2110.1 (A)
B_DVN: R2125.2, R2126.1, U2107.2 (-INA)
B_DVP: R2123.2, R2124.1, U2107.3 (+INA)
B_DV_OK: U2110.4 (Y), U2201.6 (C)
B_HOLD: U2103.4 (Y), U2202.1 (A)
B_HOLDN: U2102.6 (OUTB), U2103.2 (B)
B_HOLDP: U2102.7 (OUTA), U2103.1 (A)
B_IH: C2102.2, R2108.2, U2101.7 (OUTB), U2102.1 (+INA), U2102.4 (-INB), U2104.1 (+INA), U2104.4 (-INB)
B_IM: C2101.2, R2104.2, U2101.1 (OUTA)
B_IN+: F2001.1, F2003.1, X2001.1
B_IN-: F2002.1, F2004.1, X2003.1
B_K_COIL: C2201.1, D2202.2 (A), K2201.1 (COIL1), Q2203.2 (D)
B_K_G: Q2202.1 (G), R2207.1, U2202.3 (B), U2203.4 (Y)
B_K_GB: C2201.2, D2201.3 (K), Q2201.1 (G), R2205.1
B_K_H1: R2201.2, R2202.1
B_K_H2: R2202.2, R2203.1
B_K_H3: R2203.2, R2204.1, U2201.4 (Y), U2203.1 (A)
B_K_HG: U2202.4 (Y), U2203.2 (B)
B_K_LO: K2201.2 (COIL2), Q2201.3 (D), R2201.1
B_K_PD: Q2202.3 (D), R2208.1
B_K_PG: Q2203.1 (G), R2208.2, R2209.2
B_K_Z: D2202.1 (K), D2203.1 (K)
B_MON1: R2001.1, RV2001.3 (MON)
B_MON2: R2012.2, RV2002.3 (MON)
B_MON3: D2001.1 (A), RV2003.3 (MON), U2001.2 (K)
B_MONA: D2001.3 (K), R2006.2, U2001.1 (A)
B_MR1: R2001.2, R2002.1
B_MR2: R2002.2, R2003.1
B_MR3: R2003.2, R2004.1
B_MR4: R2004.2, R2005.1
B_MR5: R2005.2, R2006.1
B_MS1: R2007.2, R2008.1
B_MS2: R2008.2, R2009.1
B_MS3: R2009.2, R2010.1
B_MS4: R2010.2, R2011.1
B_MS5: R2011.2, R2012.1
B_OC: U2105.4 (Y)
B_OCN: U2104.6 (OUTB), U2105.2 (B)
B_OCP: U2104.7 (OUTA), U2105.1 (A)
B_POL_OK: U2108.7 (OUTA), U2201.3 (B), U2204.3 (B)
B_PRE_M: K2202.4 (P2), K2202.6 (P1)
B_PRE_R: K2202.2 (P2-), R2210.1
B_P_COIL: D2204.2 (A), K2202.1 (COIL), Q2205.2 (D)
B_P_G: Q2204.1 (G), R2212.1, U2204.4 (Y)
B_P_PD: Q2204.3 (D), R2213.1
B_P_PG: Q2205.1 (G), R2213.2, R2214.2
B_P_Z: D2204.1 (K), D2205.1 (K)
B_SHAN: C2101.1, R2103.2, R2104.1, U2101.2 (-INA)
B_SHAP: R2101.2, R2102.1, U2101.3 (+INA)
B_SHBN: C2102.1, R2107.2, R2108.1, U2101.6 (-INB)
B_SHBP: R2105.2, R2106.1, U2101.5 (+INB)
B_SP+: F2001.2, RV2001.1 (L), X2002.1
B_SP-: F2002.2, RV2002.1 (L), X2004.1
B_SPAREB: U2107.6 (-INB), U2107.7 (OUTB)
B_SPD_N: R2013.2, U2001.4 (C)
B_SPM: R2007.1, RV2001.2 (N), RV2002.2 (N), RV2003.1 (L)
B_T+: F2003.2, K2201.A1, K2202.8 (P1+), R2109.1
B_T-: F2004.2, R2101.1, R2105.1, RS2101.1, RS2102.1
B_VBD: C2109.1, R2121.2, R2122.1, U2106.5 (+INB)
B_VBD_1: R2116.2, R2117.1
B_VBD_2: R2117.2, R2118.1
B_VBD_3: R2118.2, R2119.1
B_VBD_4: R2119.2, R2120.1
B_VBD_5: R2120.2, R2121.1
B_VB_O: R2125.1, U2106.6 (-INB), U2106.7 (OUTB)
B_VXD: C2108.1, R2114.2, R2115.1, U2106.3 (+INA)
B_VXD_1: R2109.2, R2110.1
B_VXD_2: R2110.2, R2111.1
B_VXD_3: R2111.2, R2112.1
B_VXD_4: R2112.2, R2113.1
B_VXD_5: R2113.2, R2114.1
B_VX_O: R2123.1, U2106.1 (OUTA), U2106.2 (-INA), U2108.1 (+INA)
DC+: K2201.A2, R2116.1, R2210.2
DC-: R2103.1, R2107.1, RS2101.2, RS2102.2
D_HOLD_HI: U2102.2 (-INA)
D_HOLD_LO: U2102.3 (+INB)
D_OC_HI: U2104.2 (-INA)
D_OC_LO: U2104.3 (+INB)
D_TH_HI: U2108.2 (-INA), U2109.1 (+INA)
D_TH_LO: U2108.4 (-INB)
D_VMID: C2108.2, C2109.2, R2102.2, R2106.2, R2115.2, R2122.2, R2124.2
GND: D2201.1 (A), D2203.2 (A), D2205.2 (A), K2202.0 (COIL), Q2201.2 (S), Q2202.2 (S), Q2204.2 (S), R2204.2, R2205.2, R2206.2, R2207.2, R2211.2, R2212.2
K_B: R2206.1, U2201.1 (A)
K_PRE: R2211.1, U2204.1 (A)
PE_T: RV2003.2 (N)

Notes on the sheet:
HCHVF1000-400A-38R in both poles (aR, partial range): see the board's design check.
TVT25751 x 3 (615 VDC, thermal link + monitor lead): MOV1 +/M, MOV2 -/M, MOV3 M/PE_T. Up,eff 3793 V pole-PE and pole-pole at In 3 kA (calc., <= 4.0 kV -> reinforced 6 kV / basic 4 kV, D-032); Imax 25 kA. Branch fuses ETI CH14x51 gPV 36 A 30 kA (L/R 2 ms). Monitor loop through both fuses and all thr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
AR FUSES (BATTERY-TYPE PORT)
PORT B (BATTERY SOURCE), D-044 LEAN PORT
ON-BOARD SURGE PROTECTION: VARISTOR Y (IC-01, IC-12)
Terminal side B_IN+ / B_IN-, bank DC+. HCHVF1000-400A-38R aR in both poles. Contactor opens <= 0.97 kA, held above (port_spec lean). Fuse / contactor coordination: the board's design check.
