vectivolt/PCM/hardware/PCS-PWR-4W/sheets/23_dcterm.kicad_sch

## KiCad design hardware/PCS-PWR-4W/sheets/23_dcterm.kicad_sch (2026-10-07)

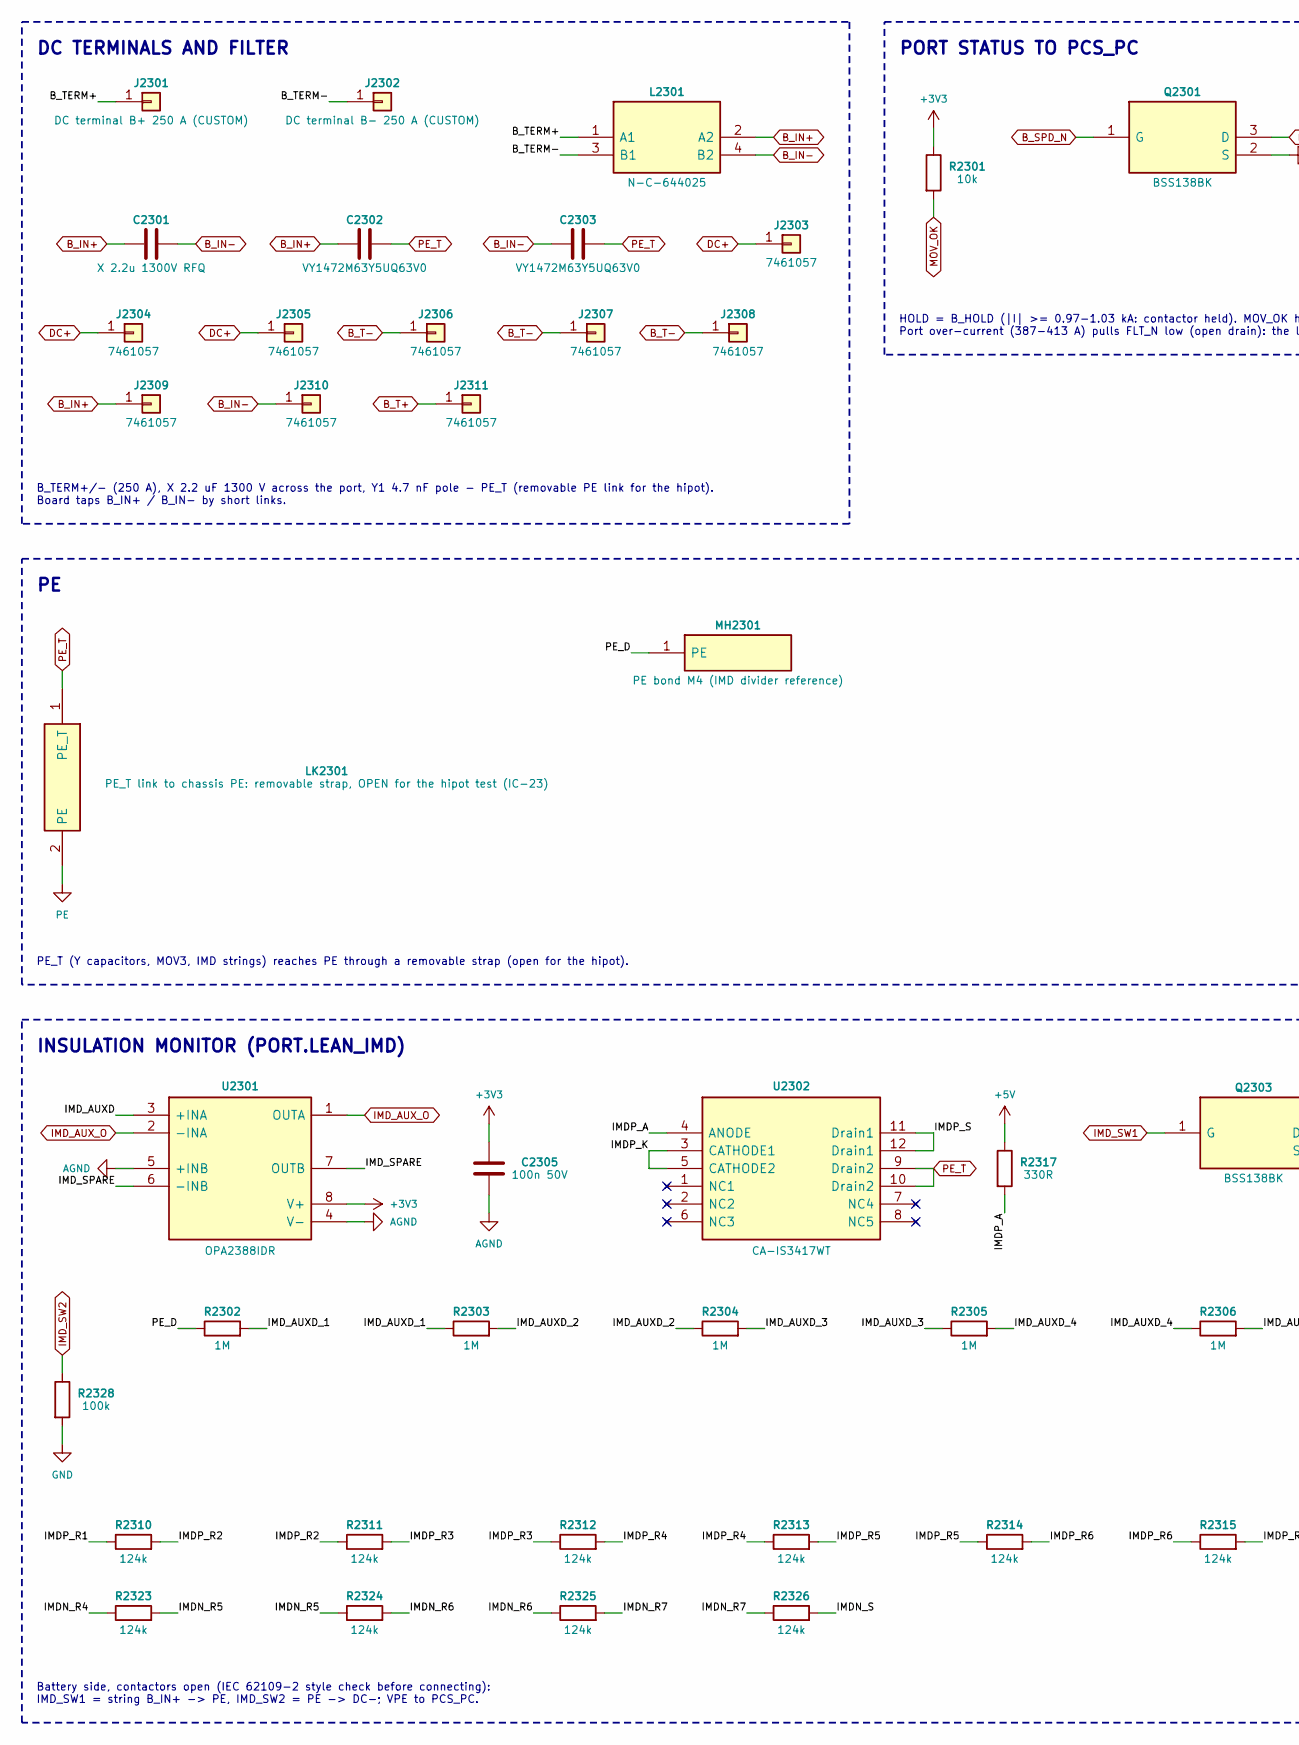
[picture p339: schematic 23_dcterm.kicad_sch, part in row 1, column 1]

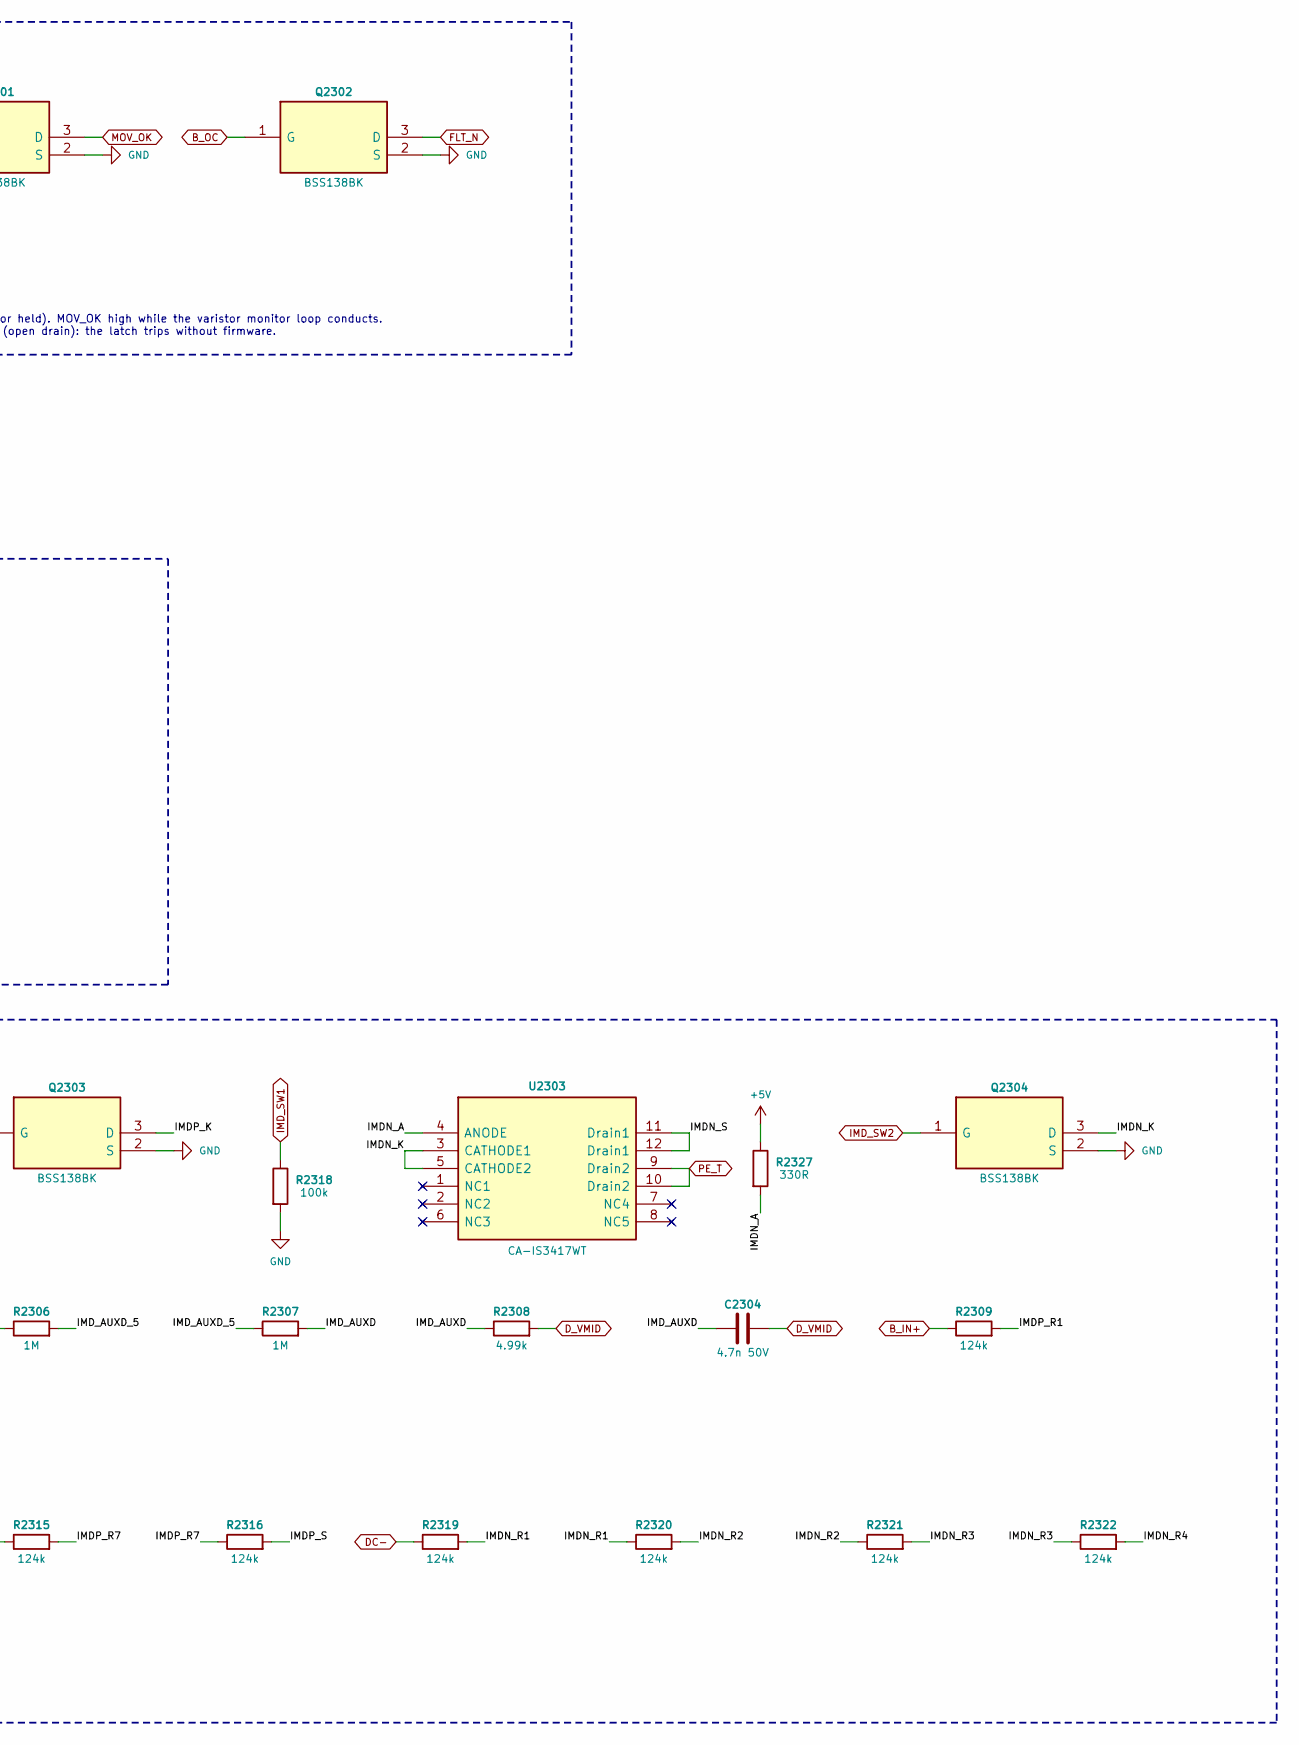
[picture p340: schematic 23_dcterm.kicad_sch, part in row 1, column 2]

Parts:
C2301: X 2.2u 1300V RFQ
C2302, C2303: VY1472M63Y5UQ63V0; MPN VY1472M63Y5UQ63V0
C2304: 4.7n 50V
C2305: 100n 50V
J2301: DC terminal B+ 250 A (CUSTOM)
J2302: DC terminal B- 250 A (CUSTOM)
J2303, J2304, J2305, J2306, J2307, J2308, J2309, J2310, J2311: 7461057; MPN 7461057
L2301: N-C-644025; MPN N-C-644025
LK2301: PE_T link to chassis PE: removable strap, OPEN fo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
MH2301: PE bond M4 (IMD divider reference)
Q2301, Q2302, Q2303, Q2304: BSS138BK; MPN BSS138BK
R2301: 10k
R2302, R2303, R2304, R2305, R2306, R2307: 1M; MPN ARHV06BTC1004A
R2308: 4.99k; MPN TNPW12064K99BEEA
R2309, R2310, R2311, R2312, R2313, R2314, R2315, R2316, R2319, R2320, R2321, R2322, R2323, R2324, R2325, R2326: 124k; MPN ARHV13BTC1243A
R2317, R2327: 330R
R2318, R2328: 100k
U2301: OPA2388IDR; MPN OPA2388IDR
U2302, U2303: CA-IS3417WT; MPN CA-IS3417WT

Connections:
+3V3: C2305.1, R2301.1, U2301.8 (V+)
+5V: R2317.1, R2327.1
AGND: C2305.2, U2301.4 (V-), U2301.5 (+INB)
B_IN+: C2301.1, C2302.1, J2309.1, L2301.2 (A2), R2309.1
B_IN-: C2301.2, C2303.1, J2310.1, L2301.4 (B2)
B_OC: Q2302.1 (G)
B_SPD_N: Q2301.1 (G)
B_T+: J2311.1
B_T-: J2306.1, J2307.1, J2308.1
B_TERM+: J2301.1, L2301.1 (A1)
B_TERM-: J2302.1, L2301.3 (B1)
DC+: J2303.1, J2304.1, J2305.1
DC-: R2319.1
D_VMID: C2304.2, R2308.2
FLT_N: Q2302.3 (D)
GND: Q2301.2 (S), Q2302.2 (S), Q2303.2 (S), Q2304.2 (S), R2318.2, R2328.2
IMDN_A: R2327.2, U2303.4 (ANODE)
IMDN_K: Q2304.3 (D), U2303.3 (CATHODE1), U2303.5 (CATHODE2)
IMDN_R1: R2319.2, R2320.1
IMDN_R2: R2320.2, R2321.1
IMDN_R3: R2321.2, R2322.1
IMDN_R4: R2322.2, R2323.1
IMDN_R5: R2323.2, R2324.1
IMDN_R6: R2324.2, R2325.1
IMDN_R7: R2325.2, R2326.1
IMDN_S: R2326.2, U2303.11 (Drain1), U2303.12 (Drain1)
IMDP_A: R2317.2, U2302.4 (ANODE)
IMDP_K: Q2303.3 (D), U2302.3 (CATHODE1), U2302.5 (CATHODE2)
IMDP_R1: R2309.2, R2310.1
IMDP_R2: R2310.2, R2311.1
IMDP_R3: R2311.2, R2312.1
IMDP_R4: R2312.2, R2313.1
IMDP_R5: R2313.2, R2314.1
IMDP_R6: R2314.2, R2315.1
IMDP_R7: R2315.2, R2316.1
IMDP_S: R2316.2, U2302.11 (Drain1), U2302.12 (Drain1)
IMD_AUXD: C2304.1, R2307.2, R2308.1, U2301.3 (+INA)
IMD_AUXD_1: R2302.2, R2303.1
IMD_AUXD_2: R2303.2, R2304.1
IMD_AUXD_3: R2304.2, R2305.1
IMD_AUXD_4: R2305.2, R2306.1
IMD_AUXD_5: R2306.2, R2307.1
IMD_AUX_O: U2301.1 (OUTA), U2301.2 (-INA)
IMD_SPARE: U2301.6 (-INB), U2301.7 (OUTB)
IMD_SW1: Q2303.1 (G), R2318.1
IMD_SW2: Q2304.1 (G), R2328.1
MOV_OK: Q2301.3 (D), R2301.2
PE: LK2301.2 (PE)
PE_D: MH2301.1, R2302.1
PE_T: C2302.2, C2303.2, LK2301.1 (PE_T), U2302.9 (Drain2), U2302.10 (Drain2), U2303.9 (Drain2), U2303.10 (Drain2)

Notes on the sheet:
DC TERMINALS AND FILTER
INSULATION MONITOR (PORT.LEAN_IMD)
Battery side, contactors open (IEC 62109-2 style check before connecting): IMD_SW1 = string B_IN+ -> PE, IMD_SW2 = PE -> DC-; VPE to PCS_PC.
B_TERM+/- (250 A), X 2.2 uF 1300 V across the port, Y1 4.7 nF pole - PE_T (removable PE link for the hipot). Board taps B_IN+ / B_IN- by short links.
HOLD = B_HOLD (|I| >= 0.97-1.03 kA: contactor held). MOV_OK high while the varistor monitor loop conducts. Port over-current (387-413 A) pulls FLT_N low (open drain): the latch trips without firmware.
PORT STATUS TO PCS_PC
PE_T (Y capacitors, MOV3, IMD strings) reaches PE through a removable strap (open for the hipot).
