vectivolt/PCM/hardware/PCS-PWR-4W/sheets/24_acport.kicad_sch

## KiCad design hardware/PCS-PWR-4W/sheets/24_acport.kicad_sch (2026-10-07)

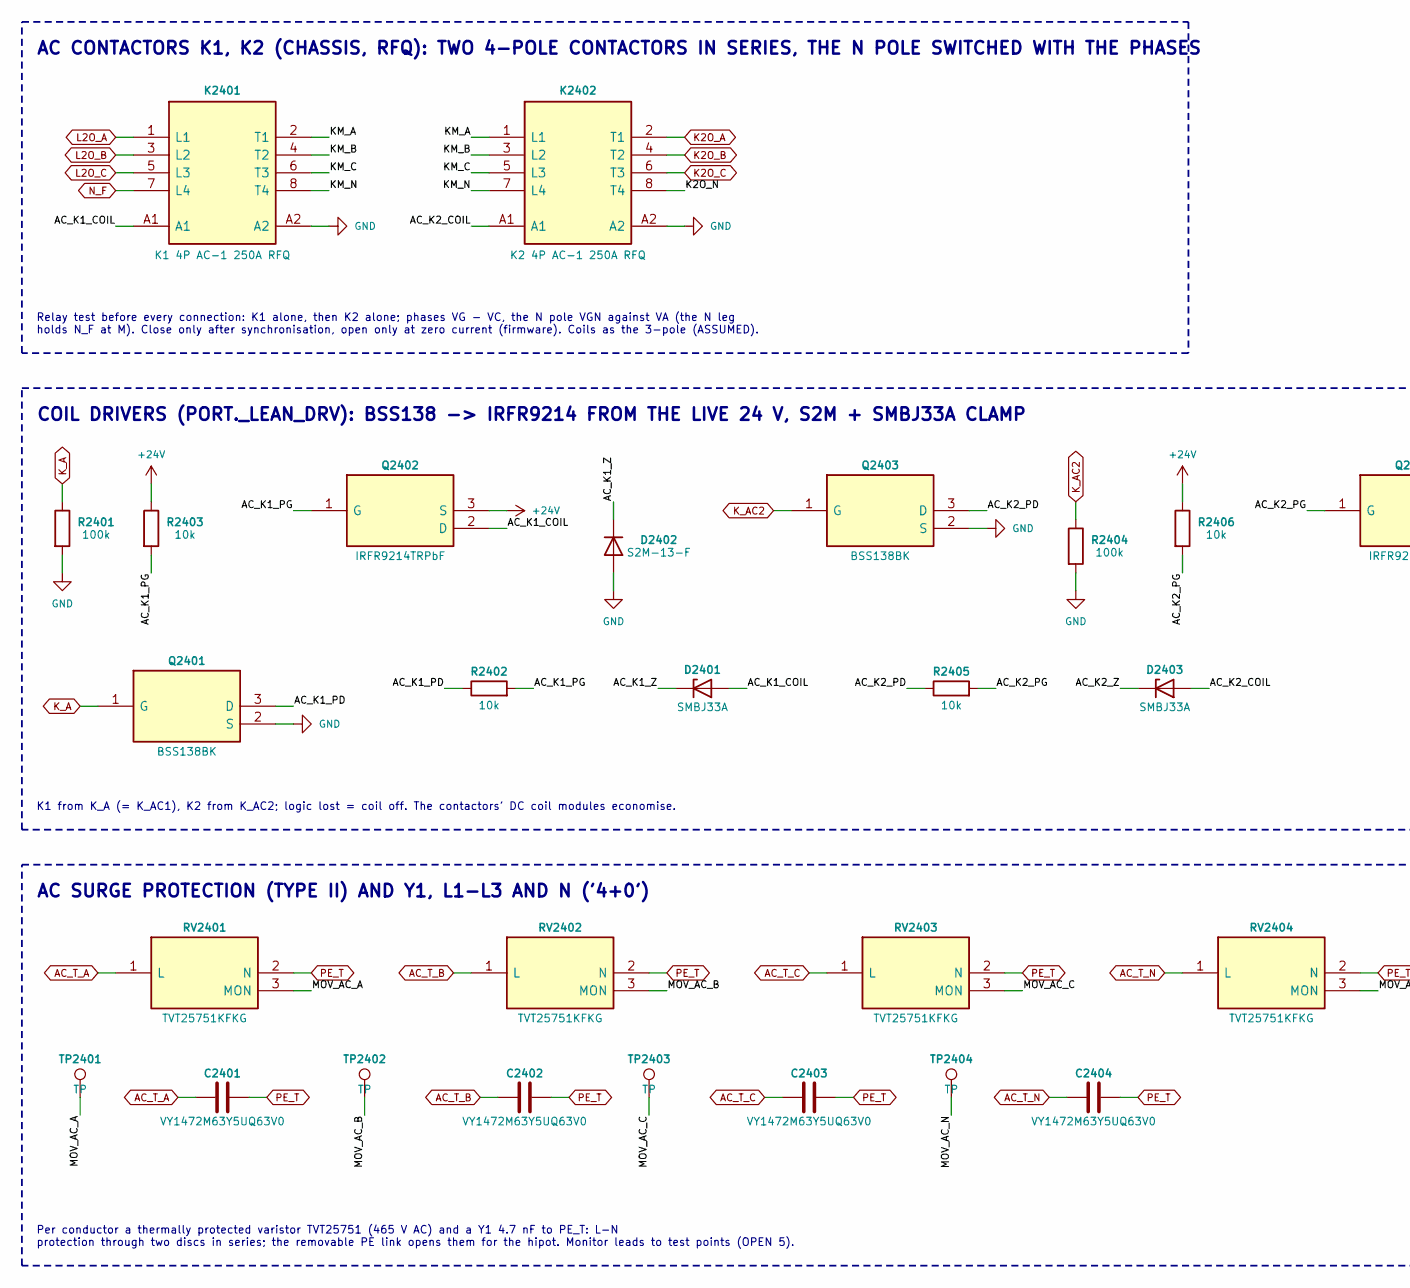
[picture p341: schematic 24_acport.kicad_sch, part in row 1, column 1]

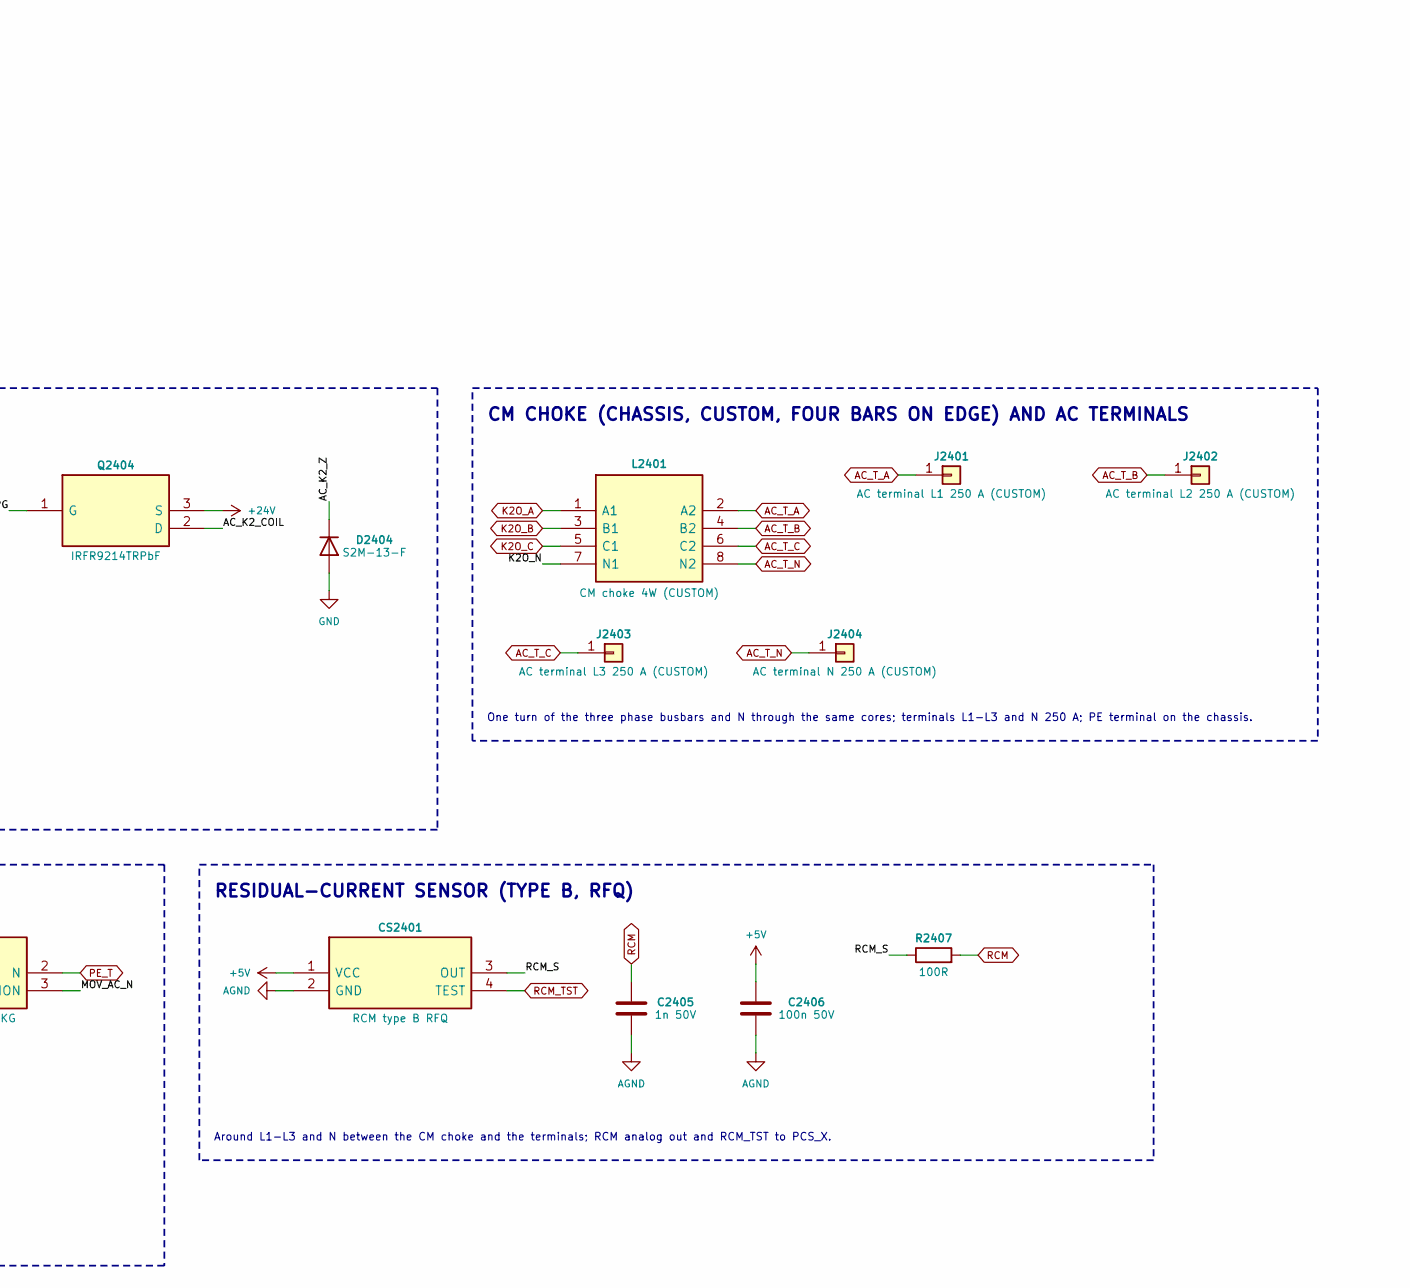
[picture p342: schematic 24_acport.kicad_sch, part in row 1, column 2]

Parts:
C2401, C2402, C2403, C2404: VY1472M63Y5UQ63V0; MPN VY1472M63Y5UQ63V0
C2405: 1n 50V
C2406: 100n 50V
CS2401: RCM type B RFQ
D2401, D2403: SMBJ33A; MPN SMBJ33A
D2402, D2404: S2M-13-F; MPN S2M-13-F
J2401: AC terminal L1 250 A (CUSTOM)
J2402: AC terminal L2 250 A (CUSTOM)
J2403: AC terminal L3 250 A (CUSTOM)
J2404: AC terminal N 250 A (CUSTOM)
K2401: K1 4P AC-1 250A RFQ
K2402: K2 4P AC-1 250A RFQ
L2401: CM choke 4W (CUSTOM)
Q2401, Q2403: BSS138BK; MPN BSS138BK
Q2402, Q2404: IRFR9214TRPbF; MPN IRFR9214TRPbF
R2401, R2404: 100k
R2402, R2403, R2405, R2406: 10k
R2407: 100R
RV2401, RV2402, RV2403, RV2404: TVT25751KFKG; MPN TVT25751KFKG
TP2401, TP2402, TP2403, TP2404: TP

Connections:
+5V: C2406.1, CS2401.1 (VCC)
+24V: Q2402.3 (S), Q2404.3 (S), R2403.1, R2406.1
AC_K1_COIL: D2401.2 (A), K2401.A1, Q2402.2 (D)
AC_K1_PD: Q2401.3 (D), R2402.1
AC_K1_PG: Q2402.1 (G), R2402.2, R2403.2
AC_K1_Z: D2401.1 (K), D2402.1 (K)
AC_K2_COIL: D2403.2 (A), K2402.A1, Q2404.2 (D)
AC_K2_PD: Q2403.3 (D), R2405.1
AC_K2_PG: Q2404.1 (G), R2405.2, R2406.2
AC_K2_Z: D2403.1 (K), D2404.1 (K)
AC_T_A: C2401.1, J2401.1, L2401.2 (A2), RV2401.1 (L)
AC_T_B: C2402.1, J2402.1, L2401.4 (B2), RV2402.1 (L)
AC_T_C: C2403.1, J2403.1, L2401.6 (C2), RV2403.1 (L)
AC_T_N: C2404.1, J2404.1, L2401.8 (N2), RV2404.1 (L)
AGND: C2405.2, C2406.2, CS2401.2 (GND)
GND: D2402.2 (A), D2404.2 (A), K2401.A2, K2402.A2, Q2401.2 (S), Q2403.2 (S), R2401.2, R2404.2
K2O_A: K2402.2 (T1), L2401.1 (A1)
K2O_B: K2402.4 (T2), L2401.3 (B1)
K2O_C: K2402.6 (T3), L2401.5 (C1)
K2O_N: K2402.8 (T4), L2401.7 (N1)
KM_A: K2401.2 (T1), K2402.1 (L1)
KM_B: K2401.4 (T2), K2402.3 (L2)
KM_C: K2401.6 (T3), K2402.5 (L3)
KM_N: K2401.8 (T4), K2402.7 (L4)
K_A: Q2401.1 (G), R2401.1
K_AC2: Q2403.1 (G), R2404.1
L2O_A: K2401.1 (L1)
L2O_B: K2401.3 (L2)
L2O_C: K2401.5 (L3)
MOV_AC_A: RV2401.3 (MON), TP2401.1
MOV_AC_B: RV2402.3 (MON), TP2402.1
MOV_AC_C: RV2403.3 (MON), TP2403.1
MOV_AC_N: RV2404.3 (MON), TP2404.1
N_F: K2401.7 (L4)
PE_T: C2401.2, C2402.2, C2403.2, C2404.2, RV2401.2 (N), RV2402.2 (N), RV2403.2 (N), RV2404.2 (N)
RCM: C2405.1, R2407.2
RCM_S: CS2401.3 (OUT), R2407.1
RCM_TST: CS2401.4 (TEST)

Notes on the sheet:
Relay test before every connection: K1 alone, then K2 alone; phases VG - VC, the N pole VGN against VA (the N leg holds N_F at M). Close only after synchronisation, open only at zero current (firmware). Coils as the 3-pole (ASSUMED).
K1 from K_A (= K_AC1), K2 from K_AC2; logic lost = coil off. The contactors' DC coil modules economise.
CM CHOKE (CHASSIS, CUSTOM, FOUR BARS ON EDGE) AND AC TERMINALS
RESIDUAL-CURRENT SENSOR (TYPE B, RFQ)
COIL DRIVERS (PORT._LEAN_DRV): BSS138 -> IRFR9214 FROM THE LIVE 24 V, S2M + SMBJ33A CLAMP
AC SURGE PROTECTION (TYPE II) AND Y1, L1-L3 AND N ('4+0')
AC CONTACTORS K1, K2 (CHASSIS, RFQ): TWO 4-POLE CONTACTORS IN SERIES, THE N POLE SWITCHED WITH THE PHASES
Around L1-L3 and N between the CM choke and the terminals; RCM analog out and RCM_TST to PCS_X.
One turn of the three phase busbars and N through the same cores; terminals L1-L3 and N 250 A; PE terminal on the chassis.
Per conductor a thermally protected varistor TVT25751 (465 V AC) and a Y1 4.7 nF to PE_T: L-N protection through two discs in series; the removable PE link opens them for the hipot. Monitor leads to test points (OPEN 5).
