vectivolt/PCM/hardware/PCS-PWR-4W/sheets/25_pe.kicad_sch

## KiCad design hardware/PCS-PWR-4W/sheets/25_pe.kicad_sch (2026-10-06)

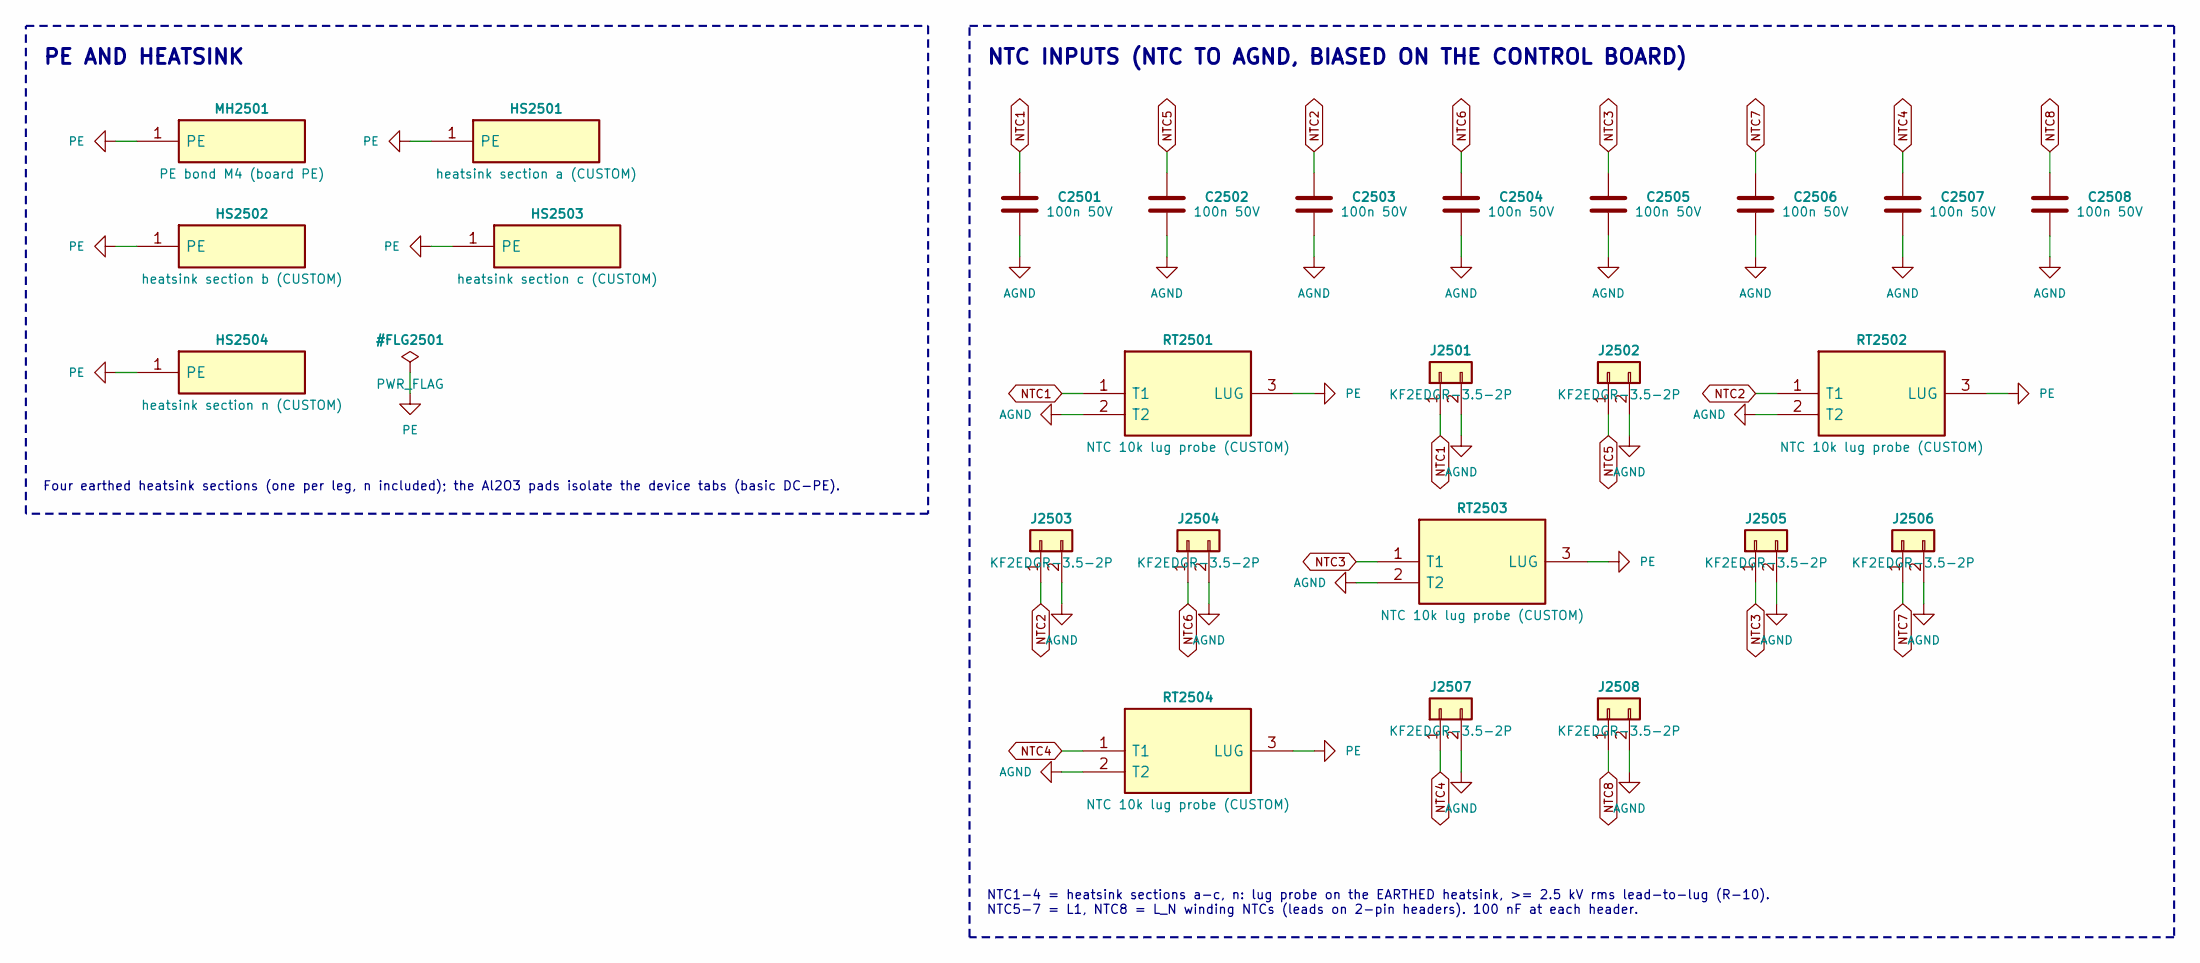
[picture p343: schematic 25_pe.kicad_sch]

Parts:
C2501, C2502, C2503, C2504, C2505, C2506, C2507, C2508: 100n 50V
HS2501: heatsink section a (CUSTOM)
HS2502: heatsink section b (CUSTOM)
HS2503: heatsink section c (CUSTOM)
HS2504: heatsink section n (CUSTOM)
J2501, J2502, J2503, J2504, J2505, J2506, J2507, J2508: KF2EDGR-3.5-2P; MPN KF2EDGR-3.5-2P
MH2501: PE bond M4 (board PE)
RT2501, RT2502, RT2503, RT2504: NTC 10k lug probe (CUSTOM)

Connections:
AGND: C2501.2, C2502.2, C2503.2, C2504.2, C2505.2, C2506.2, C2507.2, C2508.2, J2501.2, J2502.2, J2503.2, J2504.2, J2505.2, J2506.2, J2507.2, J2508.2, RT2501.2 (T2), RT2502.2 (T2), RT2503.2 (T2), RT2504.2 (T2)
NTC1: C2501.1, J2501.1, RT2501.1 (T1)
NTC2: C2503.1, J2503.1, RT2502.1 (T1)
NTC3: C2505.1, J2505.1, RT2503.1 (T1)
NTC4: C2507.1, J2507.1, RT2504.1 (T1)
NTC5: C2502.1, J2502.1
NTC6: C2504.1, J2504.1
NTC7: C2506.1, J2506.1
NTC8: C2508.1, J2508.1
PE: HS2501.1, HS2502.1, HS2503.1, HS2504.1, MH2501.1, RT2501.3 (LUG), RT2502.3 (LUG), RT2503.3 (LUG), RT2504.3 (LUG)

Notes on the sheet:
NTC1-4 = heatsink sections a-c, n: lug probe on the EARTHED heatsink, >= 2.5 kV rms lead-to-lug (R-10). NTC5-7 = L1, NTC8 = L_N winding NTCs (leads on 2-pin headers). 100 nF at each header.
NTC INPUTS (NTC TO AGND, BIASED ON THE CONTROL BOARD)
PE AND HEATSINK
Four earthed heatsink sections (one per leg, n included); the Al2O3 pads isolate the device tabs (basic DC-PE).
