vectivolt/PCM/hardware/PCS-PWR-4W/sheets/26_supplies.kicad_sch

## KiCad design hardware/PCS-PWR-4W/sheets/26_supplies.kicad_sch (2026-10-06)

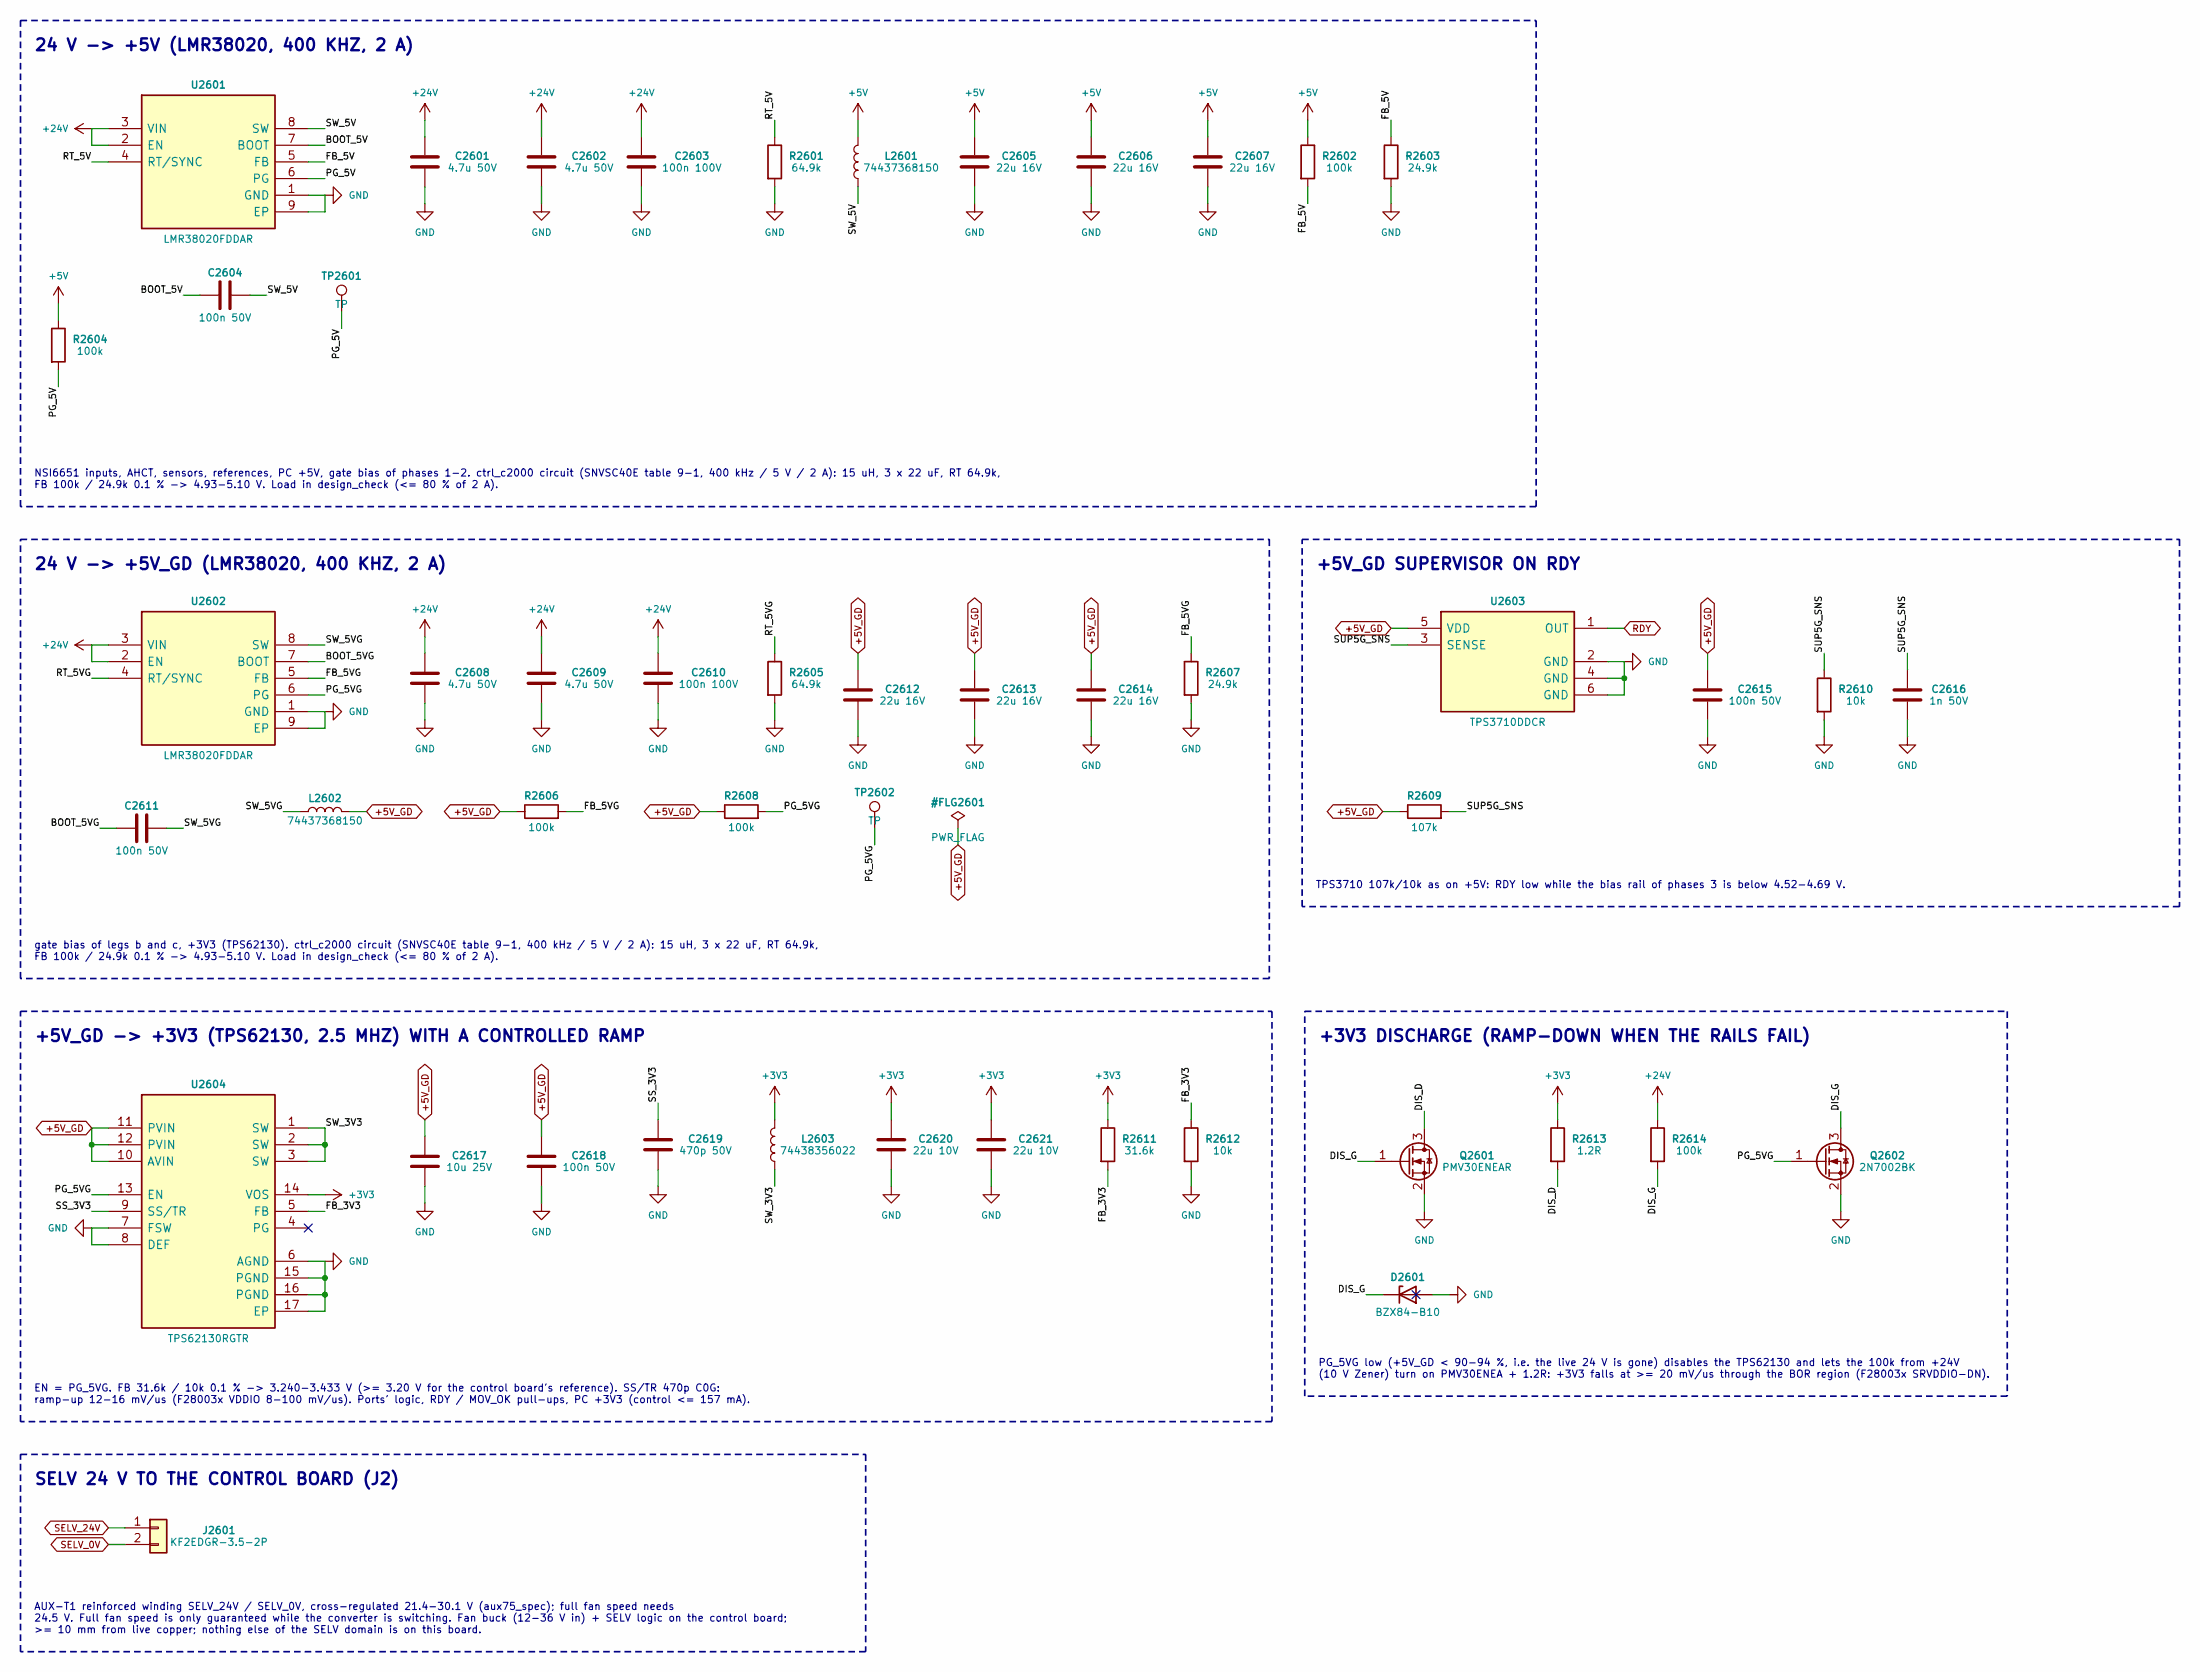
[picture p344: schematic 26_supplies.kicad_sch]

Parts:
C2601, C2602, C2608, C2609: 4.7u 50V
C2603, C2610: 100n 100V
C2604, C2611, C2615, C2618: 100n 50V
C2605, C2606, C2607, C2612, C2613, C2614: 22u 16V
C2616: 1n 50V
C2617: 10u 25V
C2619: 470p 50V
C2620, C2621: 22u 10V
D2601: BZX84-B10; MPN BZX84-B10
J2601: KF2EDGR-3.5-2P; MPN KF2EDGR-3.5-2P
L2601, L2602: 74437368150; MPN 74437368150
L2603: 74438356022; MPN 74438356022
Q2601: PMV30ENEAR; MPN PMV30ENEAR
Q2602: 2N7002BK; MPN 2N7002BK
R2601, R2605: 64.9k
R2602, R2604, R2606, R2608, R2614: 100k
R2603, R2607: 24.9k
R2609: 107k
R2610, R2612: 10k
R2611: 31.6k
R2613: 1.2R
TP2601, TP2602: TP
U2601, U2602: LMR38020FDDAR; MPN LMR38020FDDAR
U2603: TPS3710DDCR; MPN TPS3710DDCR
U2604: TPS62130RGTR; MPN TPS62130RGTR

Connections:
+3V3: C2620.1, C2621.1, L2603.2, R2611.1, R2613.1, U2604.14 (VOS)
+5V: C2605.1, C2606.1, C2607.1, L2601.2, R2602.1, R2604.1
+5V_GD: C2612.1, C2613.1, C2614.1, C2615.1, C2617.1, C2618.1, L2602.2, R2606.1, R2608.1, R2609.1, U2603.5 (VDD), U2604.10 (AVIN), U2604.11 (PVIN), U2604.12 (PVIN)
+24V: C2601.1, C2602.1, C2603.1, C2608.1, C2609.1, C2610.1, R2614.1, U2601.2 (EN), U2601.3 (VIN), U2602.2 (EN), U2602.3 (VIN)
BOOT_5V: C2604.1, U2601.7 (BOOT)
BOOT_5VG: C2611.1, U2602.7 (BOOT)
DIS_D: Q2601.3 (D), R2613.2
DIS_G: D2601.3 (K), Q2601.1 (G), Q2602.3 (D), R2614.2
FB_3V3: R2611.2, R2612.1, U2604.5 (FB)
FB_5V: R2602.2, R2603.1, U2601.5 (FB)
FB_5VG: R2606.2, R2607.1, U2602.5 (FB)
GND: C2601.2, C2602.2, C2603.2, C2605.2, C2606.2, C2607.2, C2608.2, C2609.2, C2610.2, C2612.2, C2613.2, C2614.2, C2615.2, C2616.2, C2617.2, C2618.2, C2619.2, C2620.2, C2621.2, D2601.1 (A), Q2601.2 (S), Q2602.2 (S), R2601.2, R2603.2, R2605.2, R2607.2, R2610.2, R2612.2, U2601.1 (GND), U2601.9 (EP), U2602.1 (GND), U2602.9 (EP), U2603.2 (GND), U2603.4 (GND), U2603.6 (GND), U2604.6 (AGND), U2604.7 (FSW), U2604.8 (DEF), U2604.15 (PGND), U2604.16 (PGND), U2604.17 (EP)
PG_5V: R2604.2, TP2601.1, U2601.6 (PG)
PG_5VG: Q2602.1 (G), R2608.2, TP2602.1, U2602.6 (PG), U2604.13 (EN)
RDY: U2603.1 (OUT)
RT_5V: R2601.1, U2601.4 (RT/SYNC)
RT_5VG: R2605.1, U2602.4 (RT/SYNC)
SELV_0V: J2601.2
SELV_24V: J2601.1
SS_3V3: C2619.1, U2604.9 (SS/TR)
SUP5G_SNS: C2616.1, R2609.2, R2610.1, U2603.3 (SENSE)
SW_3V3: L2603.1, U2604.1 (SW), U2604.2 (SW), U2604.3 (SW)
SW_5V: C2604.2, L2601.1, U2601.8 (SW)
SW_5VG: C2611.2, L2602.1, U2602.8 (SW)

Notes on the sheet:
NSI6651 inputs, AHCT, sensors, references, PC +5V, gate bias of phases 1-2. ctrl_c2000 circuit (SNVSC40E table 9-1, 400 kHz / 5 V / 2 A): 15 uH, 3 x 22 uF, RT 64.9k, FB 100k / 24.9k 0.1 % -> 4.93-5.10 V. Load in design_check (<= 80 % of 2 A).
PG_5VG low (+5V_GD < 90-94 %, i.e. the live 24 V is gone) disables the TPS62130 and lets the 100k from +24V (10 V Zener) turn on PMV30ENEA + 1.2R: +3V3 falls at >= 20 mV/us through the BOR region (F28003x SRVDDIO-DN).
AUX-T1 reinforced winding SELV_24V / SELV_0V, cross-regulated 21.4-30.1 V (aux75_spec); full fan speed needs 24.5 V. Full fan speed is only guaranteed while the converter is switching. Fan buck (12-36 V in) + SELV logic on the control board; >= 10 mm from live copper; nothing else of the SELV domai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
gate bias of legs b and c, +3V3 (TPS62130). ctrl_c2000 circuit (SNVSC40E table 9-1, 400 kHz / 5 V / 2 A): 15 uH, 3 x 22 uF, RT 64.9k, FB 100k / 24.9k 0.1 % -> 4.93-5.10 V. Load in design_check (<= 80 % of 2 A).
+3V3 DISCHARGE (RAMP-DOWN WHEN THE RAILS FAIL)
+5V_GD -> +3V3 (TPS62130, 2.5 MHZ) WITH A CONTROLLED RAMP
+5V_GD SUPERVISOR ON RDY
SELV 24 V TO THE CONTROL BOARD (J2)
TPS3710 107k/10k as on +5V: RDY low while the bias rail of phases 3 is below 4.52-4.69 V.
EN = PG_5VG. FB 31.6k / 10k 0.1 % -> 3.240-3.433 V (>= 3.20 V for the control board's reference). SS/TR 470p C0G: ramp-up 12-16 mV/us (F28003x VDDIO 8-100 mV/us). Ports' logic, RDY / MOV_OK pull-ups, PC +3V3 (control <= 157 mA).
24 V -> +5V (LMR38020, 400 KHZ, 2 A)
24 V -> +5V_GD (LMR38020, 400 KHZ, 2 A)
