vectivolt/PCM/hardware/PCS-PWR-4W/sheets/27_aux75_input.kicad_sch

## KiCad design hardware/PCS-PWR-4W/sheets/27_aux75_input.kicad_sch (2026-10-06)

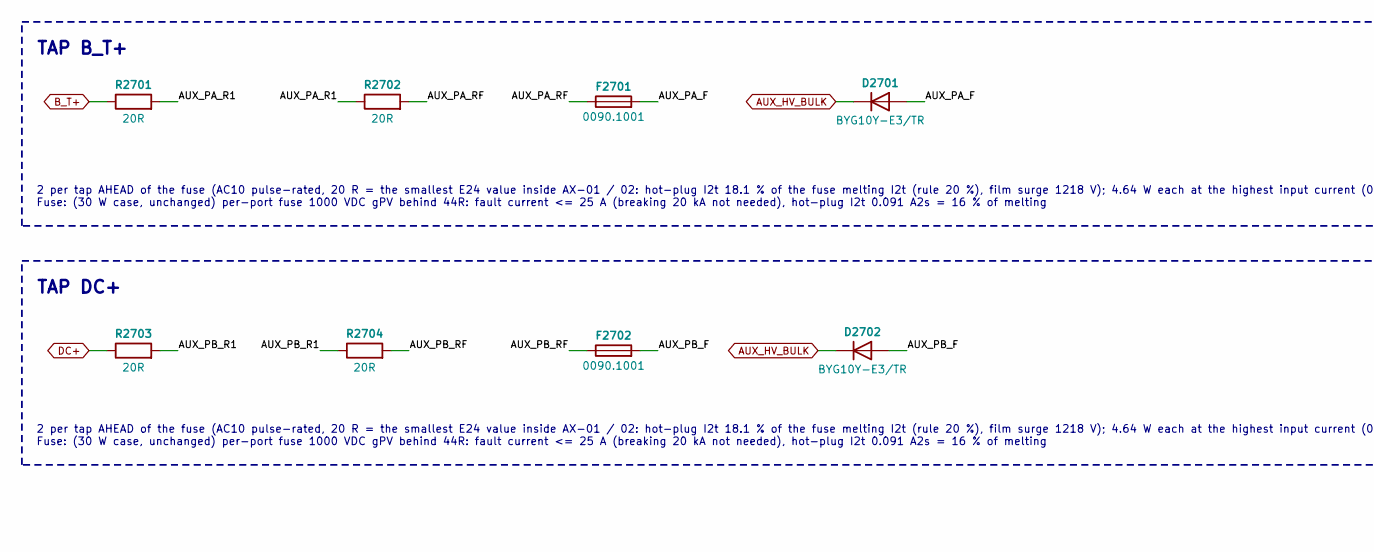
[picture p345: schematic 27_aux75_input.kicad_sch, part in row 1, column 1]

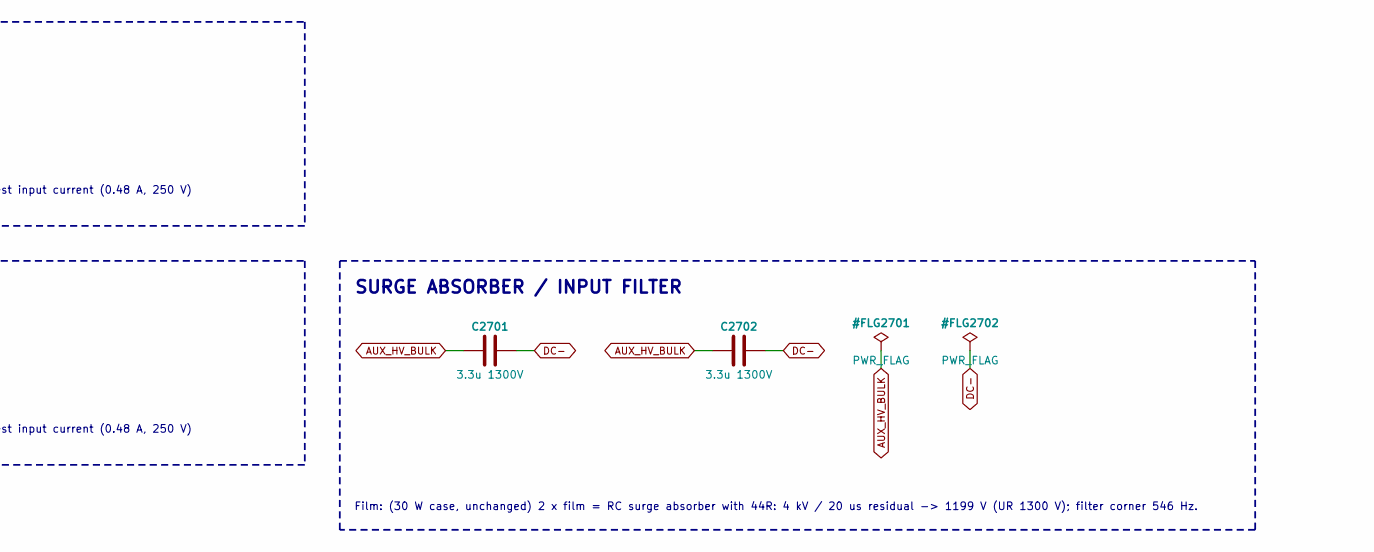
[picture p346: schematic 27_aux75_input.kicad_sch, part in row 1, column 2]

Parts:
C2701, C2702: 3.3u 1300V; MPN FCSA3DS335K050ID90BE3
D2701, D2702: BYG10Y-E3/TR; MPN BYG10Y-E3/TR
F2701, F2702: 0090.1001; MPN 0090.1001
R2701, R2702, R2703, R2704: 20R; MPN AC10000002009JAB00

Connections:
AUX_HV_BULK: C2701.1, C2702.1, D2701.1 (K), D2702.1 (K)
AUX_PA_F: D2701.2 (A), F2701.2
AUX_PA_R1: R2701.2, R2702.1
AUX_PA_RF: F2701.1, R2702.2
AUX_PB_F: D2702.2 (A), F2702.2
AUX_PB_R1: R2703.2, R2704.1
AUX_PB_RF: F2702.1, R2704.2
B_T+: R2701.1
DC+: R2703.1
DC-: C2701.2, C2702.2

Notes on the sheet:
SURGE ABSORBER / INPUT FILTER
TAP DC+
Film: (30 W case, unchanged) 2 x film = RC surge absorber with 44R: 4 kV / 20 us residual -> 1199 V (UR 1300 V); filter corner 546 Hz.
TAP B_T+
2 per tap AHEAD of the fuse (AC10 pulse-rated, 20 R = the smallest E24 value inside AX-01 / 02: hot-plug I2t 18.1 % of the fuse melting I2t (rule 20 %), film surge 1218 V); 4.64 W each at the highest input current (0.48 A, 250 V) Fuse: (30 W case, unchanged) per-port fuse 1000 VDC gPV behind 44R: f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
