vectivolt/PCM/hardware/PCS-PWR-4W/sheets/28_aux75_startup.kicad_sch

## KiCad design hardware/PCS-PWR-4W/sheets/28_aux75_startup.kicad_sch (2026-10-06)

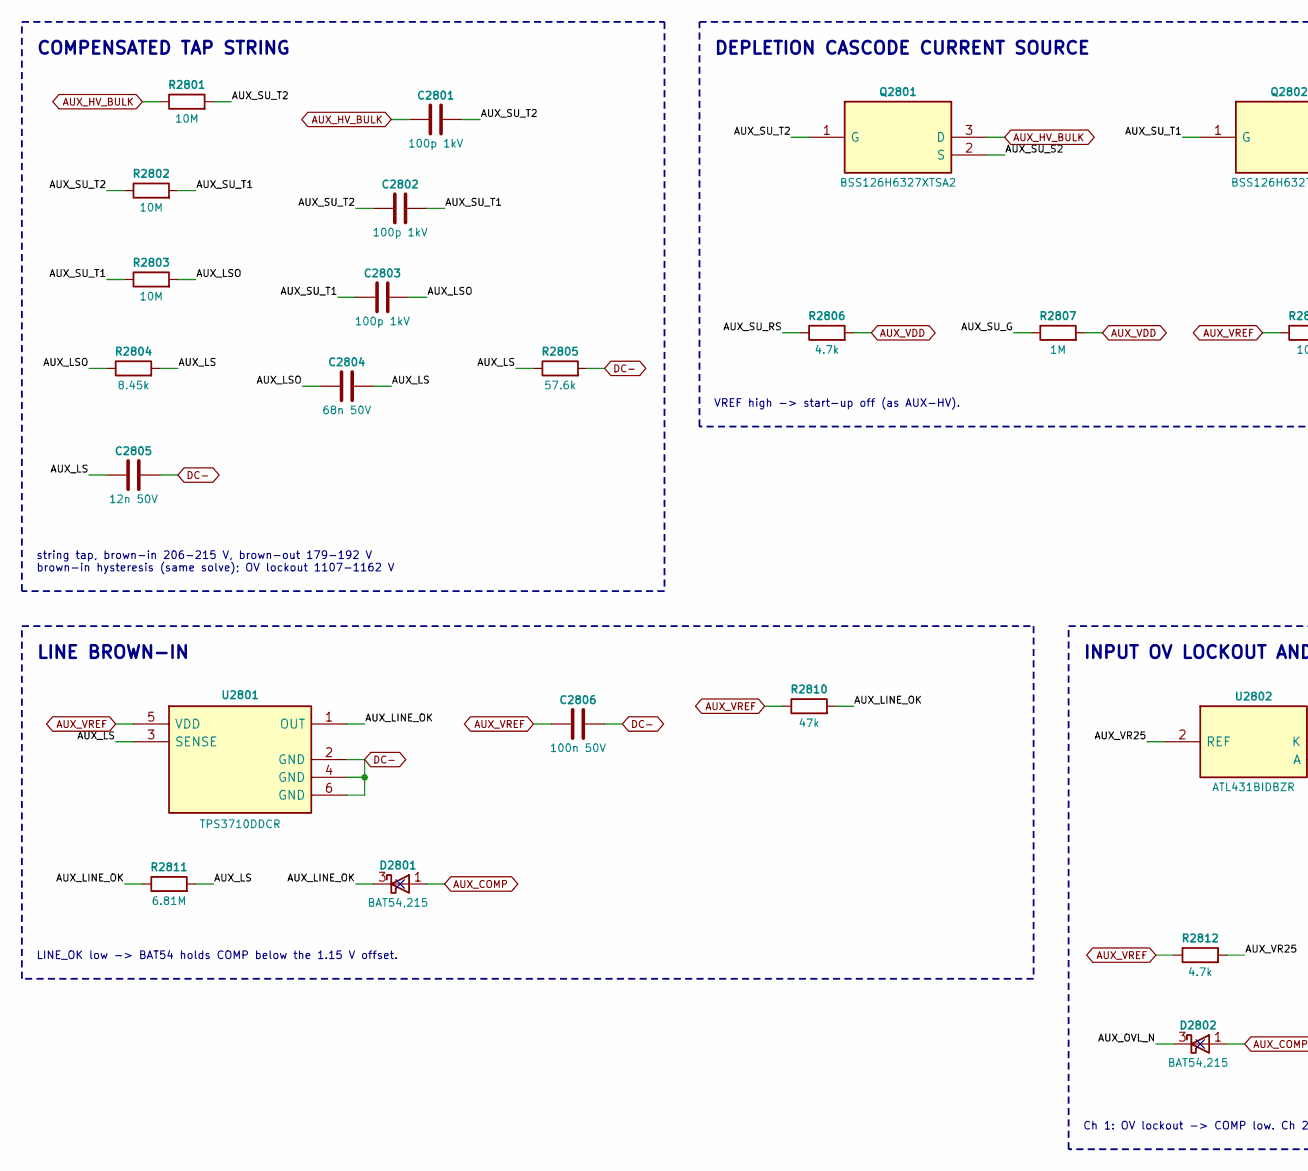
[picture p347: schematic 28_aux75_startup.kicad_sch, part in row 1, column 1]

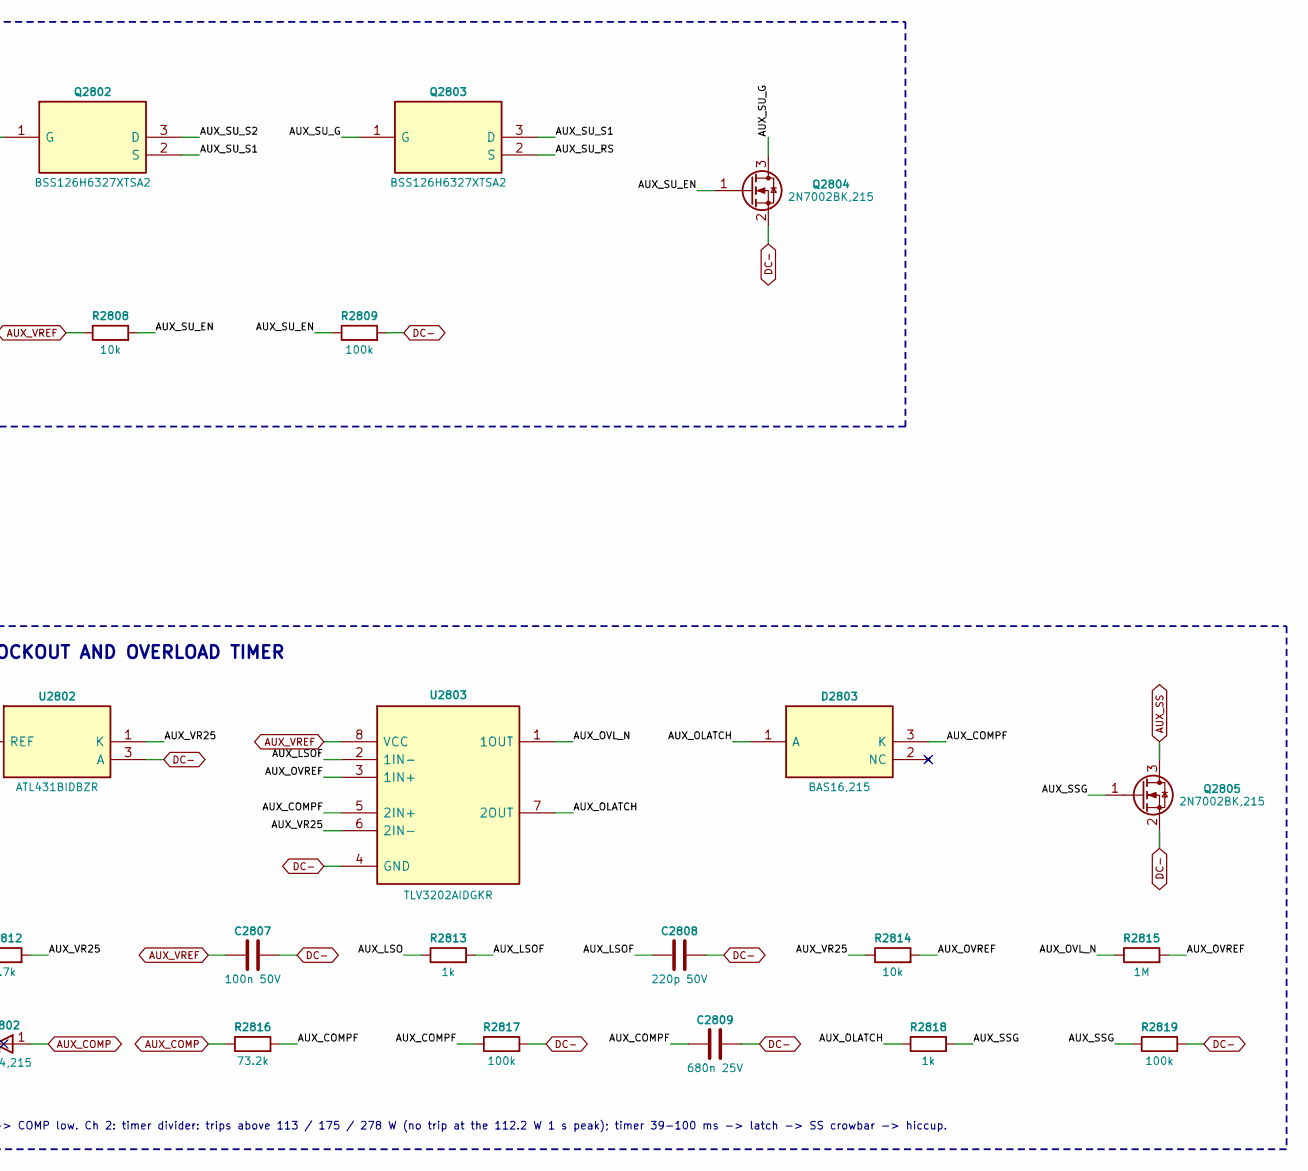
[picture p348: schematic 28_aux75_startup.kicad_sch, part in row 1, column 2]

Parts:
C2801, C2802, C2803: 100p 1kV
C2804: 68n 50V
C2805: 12n 50V
C2806, C2807: 100n 50V
C2808: 220p 50V
C2809: 680n 25V
D2801, D2802: BAT54,215; MPN BAT54,215
D2803: BAS16,215; MPN BAS16,215
Q2801, Q2802, Q2803: BSS126H6327XTSA2; MPN BSS126H6327XTSA2
Q2804, Q2805: 2N7002BK,215; MPN 2N7002BK,215
R2801, R2802, R2803: 10M; MPN CRHV2512AF10M0FKFB
R2804: 8.45k
R2805: 57.6k
R2806, R2812: 4.7k
R2807, R2815: 1M
R2808, R2814: 10k
R2809, R2817, R2819: 100k
R2810: 47k
R2811: 6.81M
R2813, R2818: 1k
R2816: 73.2k
U2801: TPS3710DDCR; MPN TPS3710DDCR
U2802: ATL431BIDBZR; MPN ATL431BIDBZR
U2803: TLV3202AIDGKR; MPN TLV3202AIDGKR

Connections:
AUX_COMP: D2801.1 (A), D2802.1 (A), R2816.1
AUX_COMPF: C2809.1, D2803.3 (K), R2816.2, R2817.1, U2803.5 (2IN+)
AUX_HV_BULK: C2801.1, Q2801.3 (D), R2801.1
AUX_LINE_OK: D2801.3 (K), R2810.2, R2811.1, U2801.1 (OUT)
AUX_LS: C2804.2, C2805.1, R2804.2, R2805.1, R2811.2, U2801.3 (SENSE)
AUX_LSO: C2803.2, C2804.1, R2803.2, R2804.1, R2813.1
AUX_LSOF: C2808.1, R2813.2, U2803.2 (1IN-)
AUX_OLATCH: D2803.1 (A), R2818.1, U2803.7 (2OUT)
AUX_OVL_N: D2802.3 (K), R2815.1, U2803.1 (1OUT)
AUX_OVREF: R2814.2, R2815.2, U2803.3 (1IN+)
AUX_SS: Q2805.3 (D)
AUX_SSG: Q2805.1 (G), R2818.2, R2819.1
AUX_SU_EN: Q2804.1 (G), R2808.2, R2809.1
AUX_SU_G: Q2803.1 (G), Q2804.3 (D), R2807.1
AUX_SU_RS: Q2803.2 (S), R2806.1
AUX_SU_S1: Q2802.2 (S), Q2803.3 (D)
AUX_SU_S2: Q2801.2 (S), Q2802.3 (D)
AUX_SU_T1: C2802.2, C2803.1, Q2802.1 (G), R2802.2, R2803.1
AUX_SU_T2: C2801.2, C2802.1, Q2801.1 (G), R2801.2, R2802.1
AUX_VDD: R2806.2, R2807.2
AUX_VR25: R2812.2, R2814.1, U2802.1 (K), U2802.2 (REF), U2803.6 (2IN-)
AUX_VREF: C2806.1, C2807.1, R2808.1, R2810.1, R2812.1, U2801.5 (VDD), U2803.8 (VCC)
DC-: C2805.2, C2806.2, C2807.2, C2808.2, C2809.2, Q2804.2 (S), Q2805.2 (S), R2805.2, R2809.2, R2817.2, R2819.2, U2801.2 (GND), U2801.4 (GND), U2801.6 (GND), U2802.3 (A), U2803.4 (GND)

Notes on the sheet:
LINE_OK low -> BAT54 holds COMP below the 1.15 V offset.
DEPLETION CASCODE CURRENT SOURCE
COMPENSATED TAP STRING
VREF high -> start-up off (as AUX-HV).
INPUT OV LOCKOUT AND OVERLOAD TIMER
Ch 1: OV lockout -> COMP low. Ch 2: timer divider: trips above 113 / 175 / 278 W (no trip at the 112.2 W 1 s peak); timer 39-100 ms -> latch -> SS crowbar -> hiccup.
string tap, brown-in 206-215 V, brown-out 179-192 V brown-in hysteresis (same solve); OV lockout 1107-1162 V
LINE BROWN-IN
