vectivolt/PCM/hardware/PCS-PWR-4W/sheets/29_aux75_power.kicad_sch

## KiCad design hardware/PCS-PWR-4W/sheets/29_aux75_power.kicad_sch (2026-10-06)

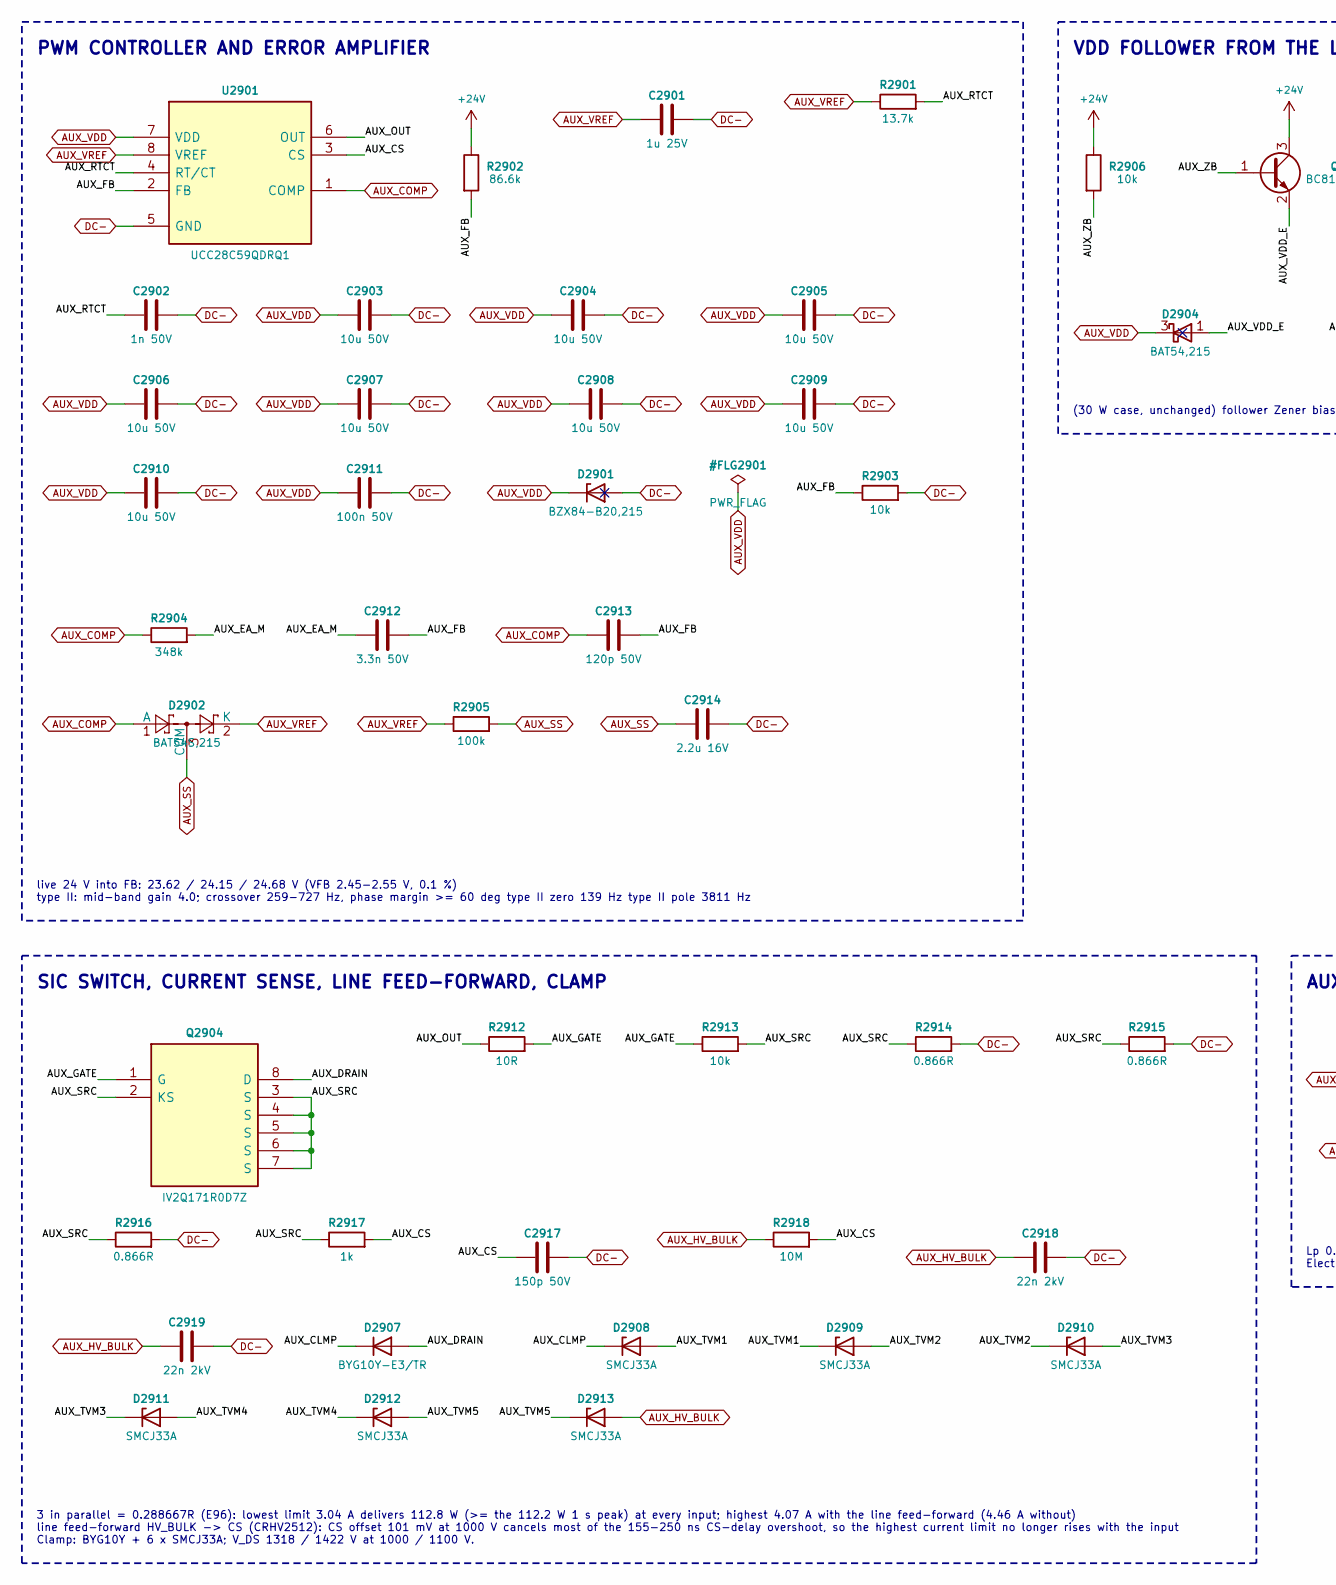
[picture p349: schematic 29_aux75_power.kicad_sch, part in row 1, column 1]

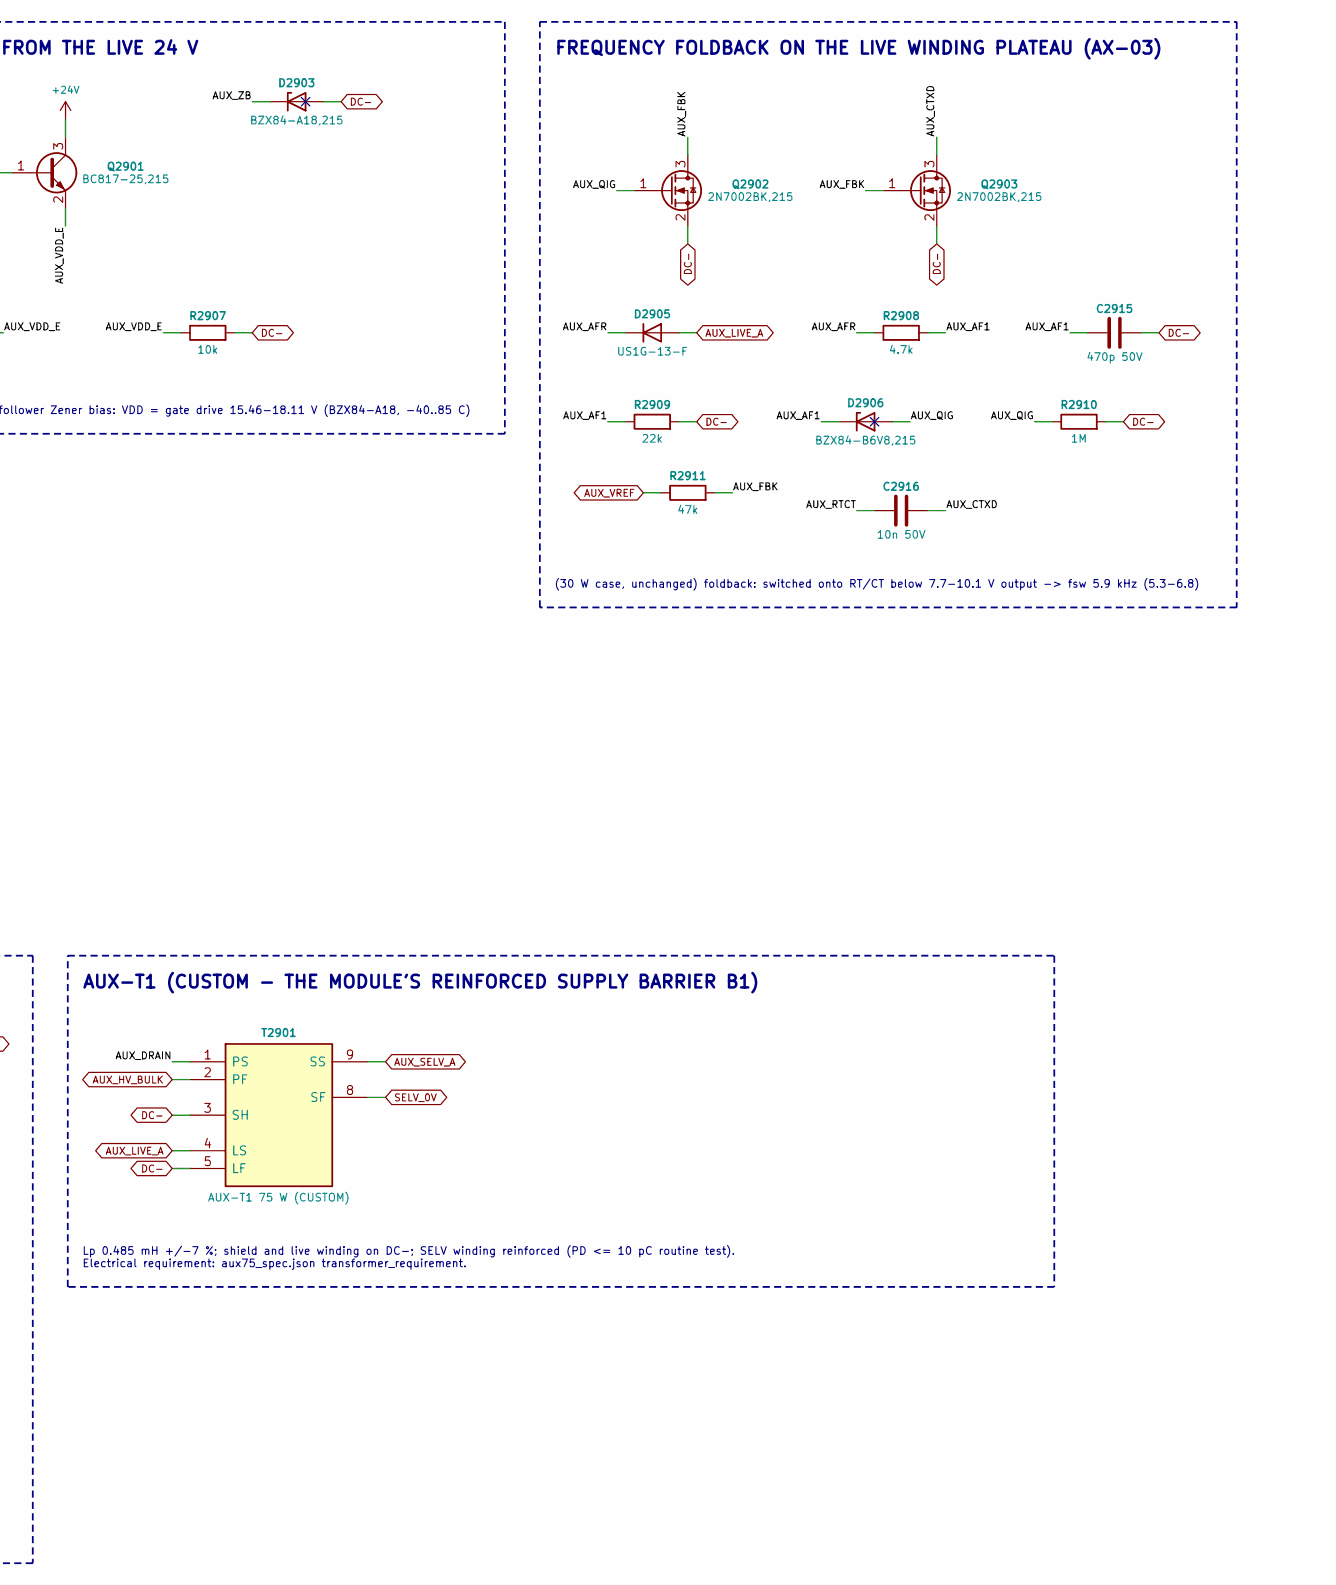
[picture p350: schematic 29_aux75_power.kicad_sch, part in row 1, column 2]

Parts:
C2901: 1u 25V
C2902: 1n 50V
C2903, C2904, C2905, C2906, C2907, C2908, C2909, C2910: 10u 50V
C2911: 100n 50V
C2912: 3.3n 50V
C2913: 120p 50V
C2914: 2.2u 16V
C2915: 470p 50V
C2916: 10n 50V
C2917: 150p 50V
C2918, C2919: 22n 2kV
D2901: BZX84-B20,215; MPN BZX84-B20,215
D2902: BAT54S,215; MPN BAT54S,215
D2903: BZX84-A18,215; MPN BZX84-A18,215
D2904: BAT54,215; MPN BAT54,215
D2905: US1G-13-F; MPN US1G-13-F
D2906: BZX84-B6V8,215; MPN BZX84-B6V8,215
D2907: BYG10Y-E3/TR; MPN BYG10Y-E3/TR
D2908, D2909, D2910, D2911, D2912, D2913: SMCJ33A; MPN SMCJ33A
Q2901: BC817-25,215; MPN BC817-25,215
Q2902, Q2903: 2N7002BK,215; MPN 2N7002BK,215
Q2904: IV2Q171R0D7Z; MPN IV2Q171R0D7Z
R2901: 13.7k
R2902: 86.6k
R2903, R2906, R2907, R2913: 10k
R2904: 348k
R2905: 100k
R2908: 4.7k
R2909: 22k
R2910: 1M
R2911: 47k
R2912: 10R
R2914, R2915, R2916: 0.866R
R2917: 1k
R2918: 10M; MPN CRHV2512AF10M0FKFB
T2901: AUX-T1 75 W (CUSTOM); MPN AUX-T1 75 W (CUSTOM)
U2901: UCC28C59QDRQ1; MPN UCC28C59QDRQ1

Connections:
+24V: Q2901.3 (C), R2902.1, R2906.1
AUX_AF1: C2915.1, D2906.3 (K), R2908.2, R2909.1
AUX_AFR: D2905.1 (K), R2908.1
AUX_CLMP: D2907.1 (K), D2908.1 (K)
AUX_COMP: C2913.1, D2902.1 (A), R2904.1, U2901.1 (COMP)
AUX_CS: C2917.1, R2917.2, R2918.2, U2901.3 (CS)
AUX_CTXD: C2916.2, Q2903.3 (D)
AUX_DRAIN: D2907.2 (A), Q2904.8 (D), T2901.1 (PS)
AUX_EA_M: C2912.1, R2904.2
AUX_FB: C2912.2, C2913.2, R2902.2, R2903.1, U2901.2 (FB)
AUX_FBK: Q2902.3 (D), Q2903.1 (G), R2911.2
AUX_GATE: Q2904.1 (G), R2912.2, R2913.1
AUX_HV_BULK: C2918.1, C2919.1, D2913.2 (A), R2918.1, T2901.2 (PF)
AUX_LIVE_A: D2905.2 (A), T2901.4 (LS)
AUX_OUT: R2912.1, U2901.6 (OUT)
AUX_QIG: D2906.1 (A), Q2902.1 (G), R2910.1
AUX_RTCT: C2902.1, C2916.1, R2901.2, U2901.4 (RT/CT)
AUX_SELV_A: T2901.9 (SS)
AUX_SRC: Q2904.2 (KS), Q2904.3 (S), Q2904.4 (S), Q2904.5 (S), Q2904.6 (S), Q2904.7 (S), R2913.2, R2914.1, R2915.1, R2916.1, R2917.1
AUX_SS: C2914.1, D2902.3 (COM), R2905.2
AUX_TVM1: D2908.2 (A), D2909.1 (K)
AUX_TVM2: D2909.2 (A), D2910.1 (K)
AUX_TVM3: D2910.2 (A), D2911.1 (K)
AUX_TVM4: D2911.2 (A), D2912.1 (K)
AUX_TVM5: D2912.2 (A), D2913.1 (K)
AUX_VDD: C2903.1, C2904.1, C2905.1, C2906.1, C2907.1, C2908.1, C2909.1, C2910.1, C2911.1, D2901.3 (K), D2904.3 (K), U2901.7 (VDD)
AUX_VDD_E: D2904.1 (A), Q2901.2 (E), R2907.1
AUX_VREF: C2901.1, D2902.2 (K), R2901.1, R2905.1, R2911.1, U2901.8 (VREF)
AUX_ZB: D2903.3 (K), Q2901.1 (B), R2906.2
DC-: C2901.2, C2902.2, C2903.2, C2904.2, C2905.2, C2906.2, C2907.2, C2908.2, C2909.2, C2910.2, C2911.2, C2914.2, C2915.2, C2917.2, C2918.2, C2919.2, D2901.1 (A), D2903.1 (A), Q2902.2 (S), Q2903.2 (S), R2903.2, R2907.2, R2909.2, R2910.2, R2914.2, R2915.2, R2916.2, T2901.3 (SH), T2901.5 (LF), U2901.5 (GND)
SELV_0V: T2901.8 (SF)

Notes on the sheet:
(30 W case, unchanged) follower Zener bias: VDD = gate drive 15.46-18.11 V (BZX84-A18, -40..85 C)
SIC SWITCH, CURRENT SENSE, LINE FEED-FORWARD, CLAMP
FREQUENCY FOLDBACK ON THE LIVE WINDING PLATEAU (AX-03)
AUX-T1 (CUSTOM - THE MODULE'S REINFORCED SUPPLY BARRIER B1)
live 24 V into FB: 23.62 / 24.15 / 24.68 V (VFB 2.45-2.55 V, 0.1 %) type II: mid-band gain 4.0; crossover 259-727 Hz, phase margin >= 60 deg type II zero 139 Hz type II pole 3811 Hz
(30 W case, unchanged) foldback: switched onto RT/CT below 7.7-10.1 V output -> fsw 5.9 kHz (5.3-6.8)
PWM CONTROLLER AND ERROR AMPLIFIER
3 in parallel = 0.288667R (E96): lowest limit 3.04 A delivers 112.8 W (>= the 112.2 W 1 s peak) at every input; highest 4.07 A with the line feed-forward (4.46 A without) line feed-forward HV_BULK -> CS (CRHV2512): CS offset 101 mV at 1000 V cancels most of the 155-250 ns CS-delay overshoot, so the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
Lp 0.485 mH +/-7 %; shield and live winding on DC-; SELV winding reinforced (PD <= 10 pC routine test). Electrical requirement: aux75_spec.json transformer_requirement.
VDD FOLLOWER FROM THE LIVE 24 V
