vectivolt/PCM/hardware/PCS-PWR-4W/sheets/30_aux75_outputs.kicad_sch

## KiCad design hardware/PCS-PWR-4W/sheets/30_aux75_outputs.kicad_sch (2026-10-06)

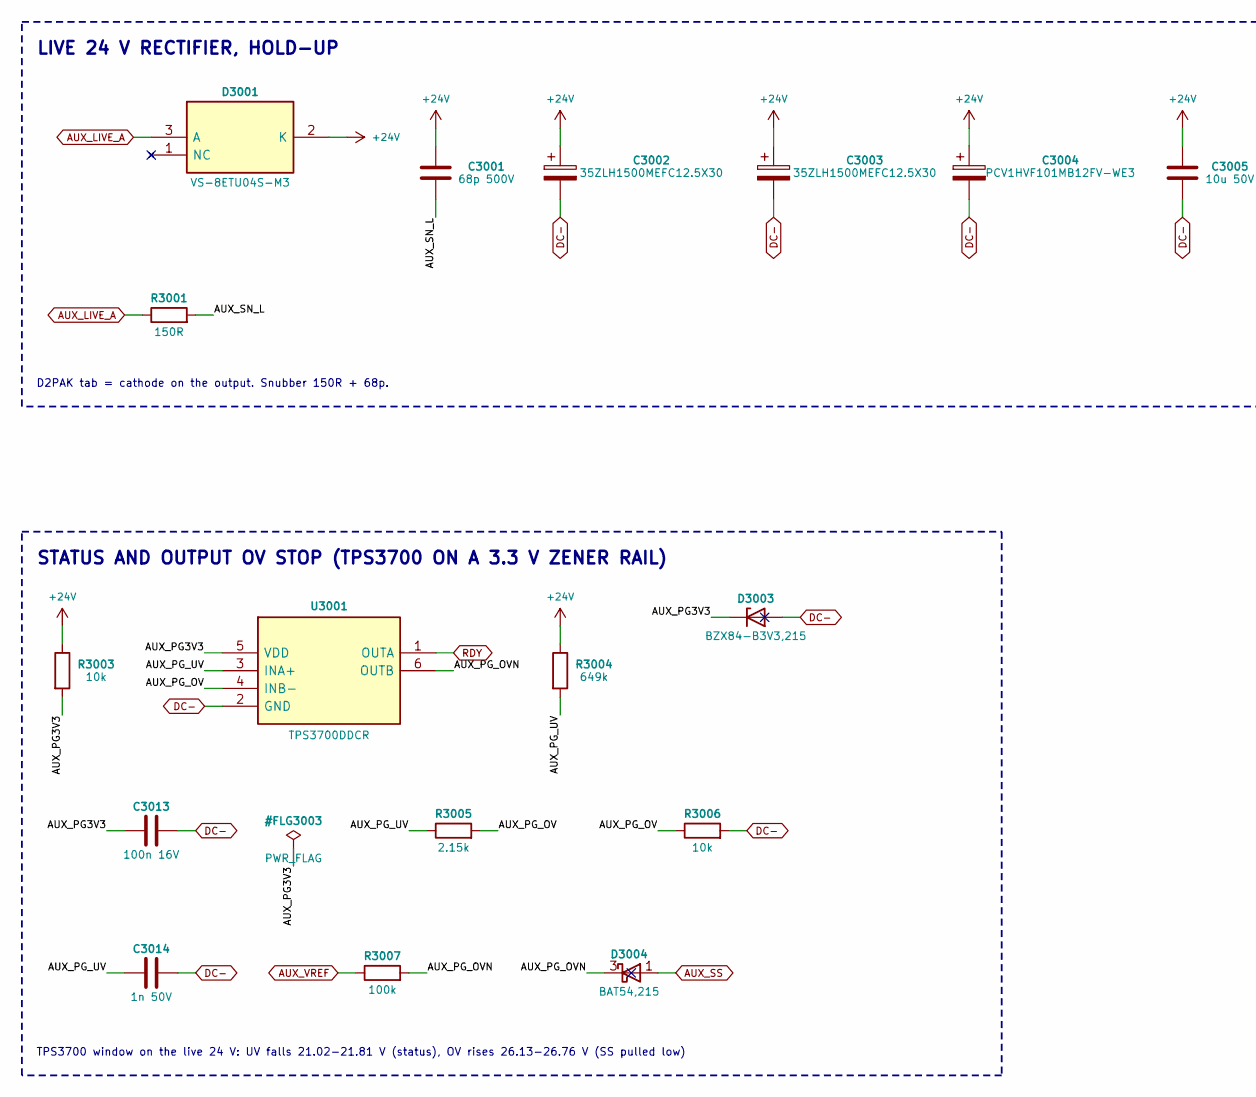
[picture p351: schematic 30_aux75_outputs.kicad_sch, part in row 1, column 1]

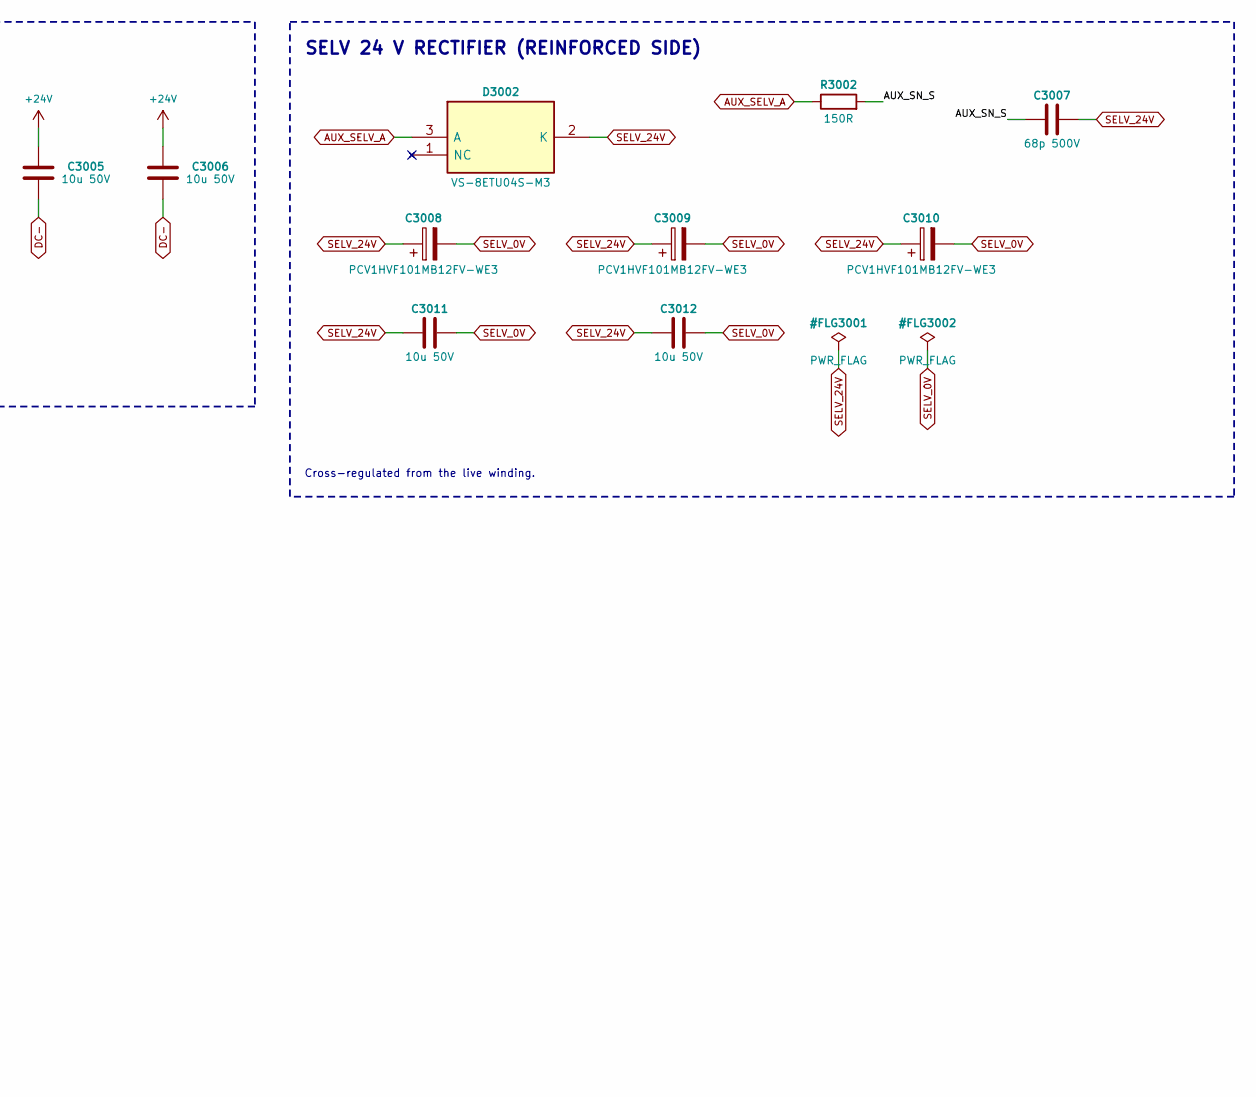
[picture p352: schematic 30_aux75_outputs.kicad_sch, part in row 1, column 2]

Parts:
C3001, C3007: 68p 500V
C3002, C3003: 35ZLH1500MEFC12.5X30; MPN 35ZLH1500MEFC12.5X30
C3004, C3008, C3009, C3010: PCV1HVF101MB12FV-WE3; MPN PCV1HVF101MB12FV-WE3
C3005, C3006, C3011, C3012: 10u 50V
C3013: 100n 16V
C3014: 1n 50V
D3001, D3002: VS-8ETU04S-M3; MPN VS-8ETU04S-M3
D3003: BZX84-B3V3,215; MPN BZX84-B3V3,215
D3004: BAT54,215; MPN BAT54,215
R3001, R3002: 150R
R3003, R3006: 10k
R3004: 649k
R3005: 2.15k
R3007: 100k
U3001: TPS3700DDCR; MPN TPS3700DDCR

Connections:
+24V: C3001.2, C3002.1, C3003.1, C3004.1, C3005.1, C3006.1, D3001.2 (K), R3003.1, R3004.1
AUX_LIVE_A: D3001.3 (A), R3001.1
AUX_PG3V3: C3013.1, D3003.3 (K), R3003.2, U3001.5 (VDD)
AUX_PG_OV: R3005.2, R3006.1, U3001.4 (INB-)
AUX_PG_OVN: D3004.3 (K), R3007.2, U3001.6 (OUTB)
AUX_PG_UV: C3014.1, R3004.2, R3005.1, U3001.3 (INA+)
AUX_SELV_A: D3002.3 (A), R3002.1
AUX_SN_L: C3001.1, R3001.2
AUX_SN_S: C3007.1, R3002.2
AUX_SS: D3004.1 (A)
AUX_VREF: R3007.1
DC-: C3002.2, C3003.2, C3004.2, C3005.2, C3006.2, C3013.2, C3014.2, D3003.1 (A), R3006.2, U3001.2 (GND)
RDY: U3001.1 (OUTA)
SELV_0V: C3008.2, C3009.2, C3010.2, C3011.2, C3012.2
SELV_24V: C3007.2, C3008.1, C3009.1, C3010.1, C3011.1, C3012.1, D3002.2 (K)

Notes on the sheet:
LIVE 24 V RECTIFIER, HOLD-UP
STATUS AND OUTPUT OV STOP (TPS3700 ON A 3.3 V ZENER RAIL)
SELV 24 V RECTIFIER (REINFORCED SIDE)
Cross-regulated from the live winding.
D2PAK tab = cathode on the output. Snubber 150R + 68p.
TPS3700 window on the live 24 V: UV falls 21.02-21.81 V (status), OV rises 26.13-26.76 V (SS pulled low)
