vectivolt/PCM/hardware/PCS-PWR-4W/sheets/31_acstart.kicad_sch

## KiCad design hardware/PCS-PWR-4W/sheets/31_acstart.kicad_sch (2026-10-06)

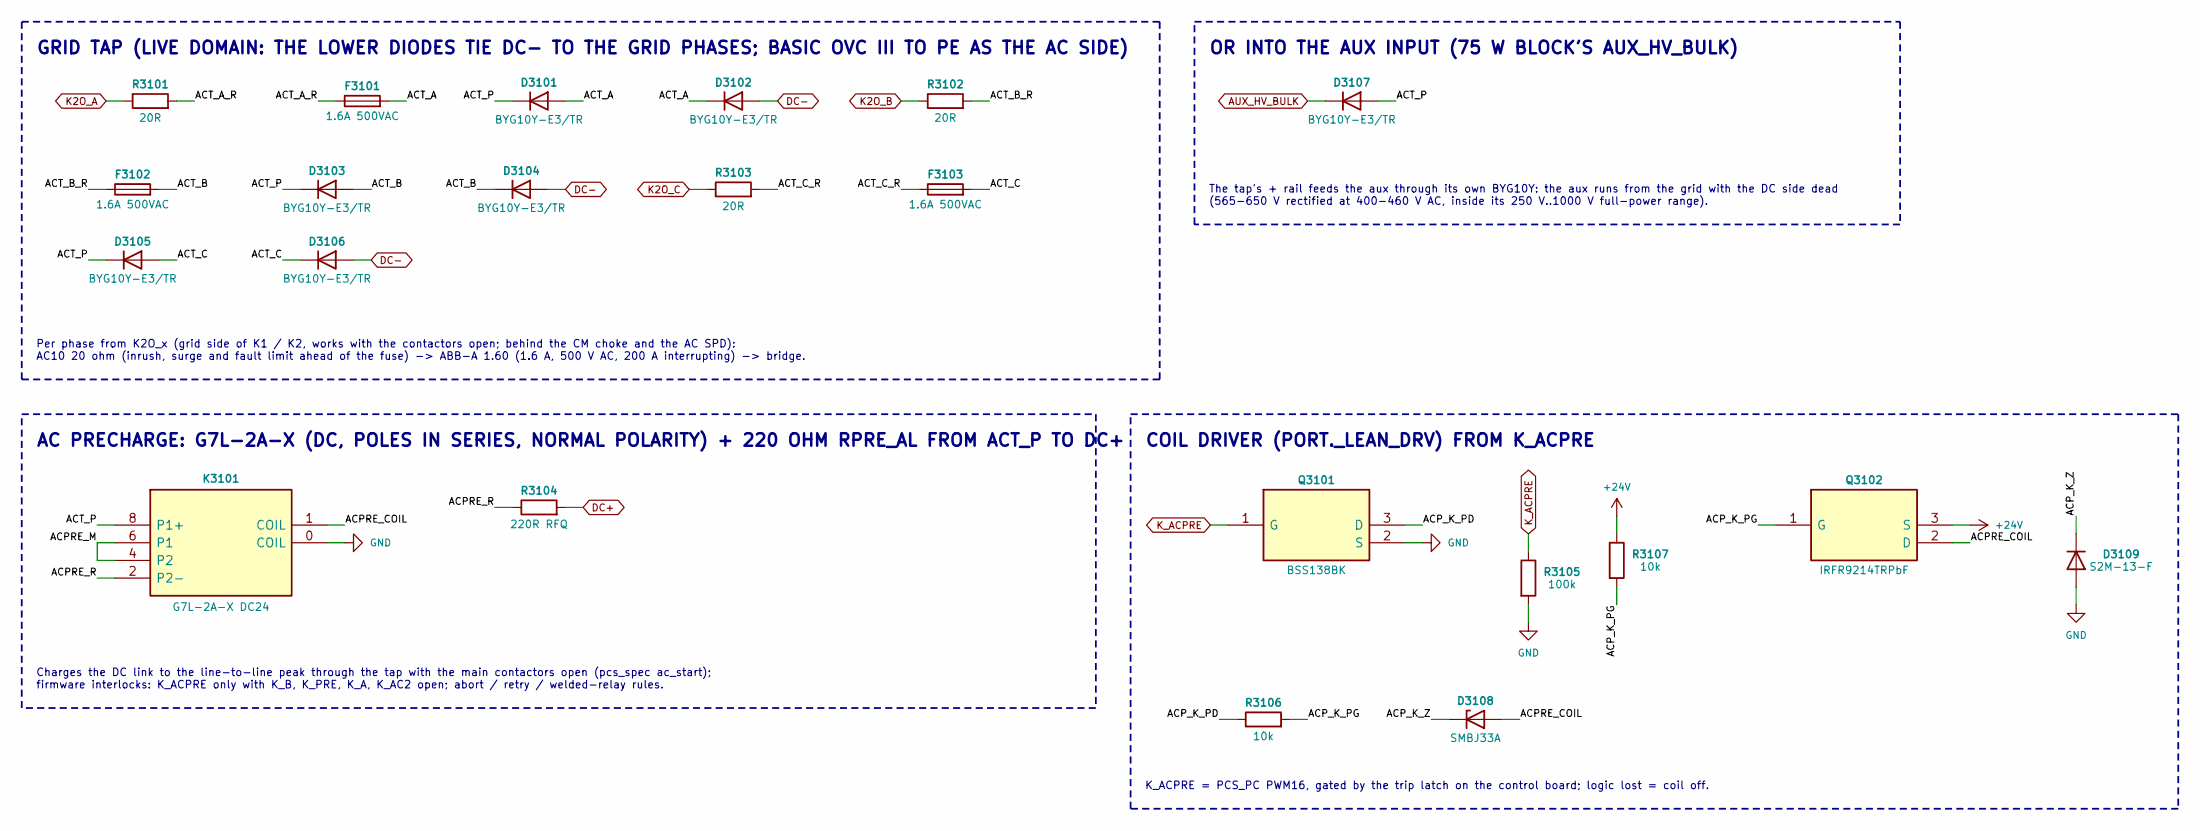
[picture p353: schematic 31_acstart.kicad_sch]

Parts:
D3101, D3102, D3103, D3104, D3105, D3106, D3107: BYG10Y-E3/TR; MPN BYG10Y-E3/TR
D3108: SMBJ33A; MPN SMBJ33A
D3109: S2M-13-F; MPN S2M-13-F
F3101, F3102, F3103: 1.6A 500VAC; MPN ABB-A 1.60
K3101: G7L-2A-X DC24; MPN G7L-2A-X DC24
Q3101: BSS138BK; MPN BSS138BK
Q3102: IRFR9214TRPbF; MPN IRFR9214TRPbF
R3101, R3102, R3103: 20R; MPN AC10000002009JAB00
R3104: 220R RFQ
R3105: 100k
R3106, R3107: 10k

Connections:
+24V: Q3102.3 (S), R3107.1
ACPRE_COIL: D3108.2 (A), K3101.1 (COIL), Q3102.2 (D)
ACPRE_M: K3101.4 (P2), K3101.6 (P1)
ACPRE_R: K3101.2 (P2-), R3104.1
ACP_K_PD: Q3101.3 (D), R3106.1
ACP_K_PG: Q3102.1 (G), R3106.2, R3107.2
ACP_K_Z: D3108.1 (K), D3109.1 (K)
ACT_A: D3101.2 (A), D3102.1 (K), F3101.2
ACT_A_R: F3101.1, R3101.2
ACT_B: D3103.2 (A), D3104.1 (K), F3102.2
ACT_B_R: F3102.1, R3102.2
ACT_C: D3105.2 (A), D3106.1 (K), F3103.2
ACT_C_R: F3103.1, R3103.2
ACT_P: D3101.1 (K), D3103.1 (K), D3105.1 (K), D3107.2 (A), K3101.8 (P1+)
AUX_HV_BULK: D3107.1 (K)
DC+: R3104.2
DC-: D3102.2 (A), D3104.2 (A), D3106.2 (A)
GND: D3109.2 (A), K3101.0 (COIL), Q3101.2 (S), R3105.2
K2O_A: R3101.1
K2O_B: R3102.1
K2O_C: R3103.1
K_ACPRE: Q3101.1 (G), R3105.1

Notes on the sheet:
Per phase from K2O_x (grid side of K1 / K2, works with the contactors open; behind the CM choke and the AC SPD): AC10 20 ohm (inrush, surge and fault limit ahead of the fuse) -> ABB-A 1.60 (1.6 A, 500 V AC, 200 A interrupting) -> bridge.
Charges the DC link to the line-to-line peak through the tap with the main contactors open (pcs_spec ac_start); firmware interlocks: K_ACPRE only with K_B, K_PRE, K_A, K_AC2 open; abort / retry / welded-relay rules.
COIL DRIVER (PORT._LEAN_DRV) FROM K_ACPRE
The tap's + rail feeds the aux through its own BYG10Y: the aux runs from the grid with the DC side dead (565-650 V rectified at 400-460 V AC, inside its 250 V..1000 V full-power range).
AC PRECHARGE: G7L-2A-X (DC, POLES IN SERIES, NORMAL POLARITY) + 220 OHM RPRE_AL FROM ACT_P TO DC+
OR INTO THE AUX INPUT (75 W BLOCK'S AUX_HV_BULK)
GRID TAP (LIVE DOMAIN: THE LOWER DIODES TIE DC- TO THE GRID PHASES; BASIC OVC III TO PE AS THE AC SIDE)
K_ACPRE = PCS_PC PWM16, gated by the trip latch on the control board; logic lost = coil off.
