vectivolt/PCM/hardware/PCS-PWR/sheets/02_dclink.kicad_sch

## KiCad design hardware/PCS-PWR/sheets/02_dclink.kicad_sch (2026-10-06)

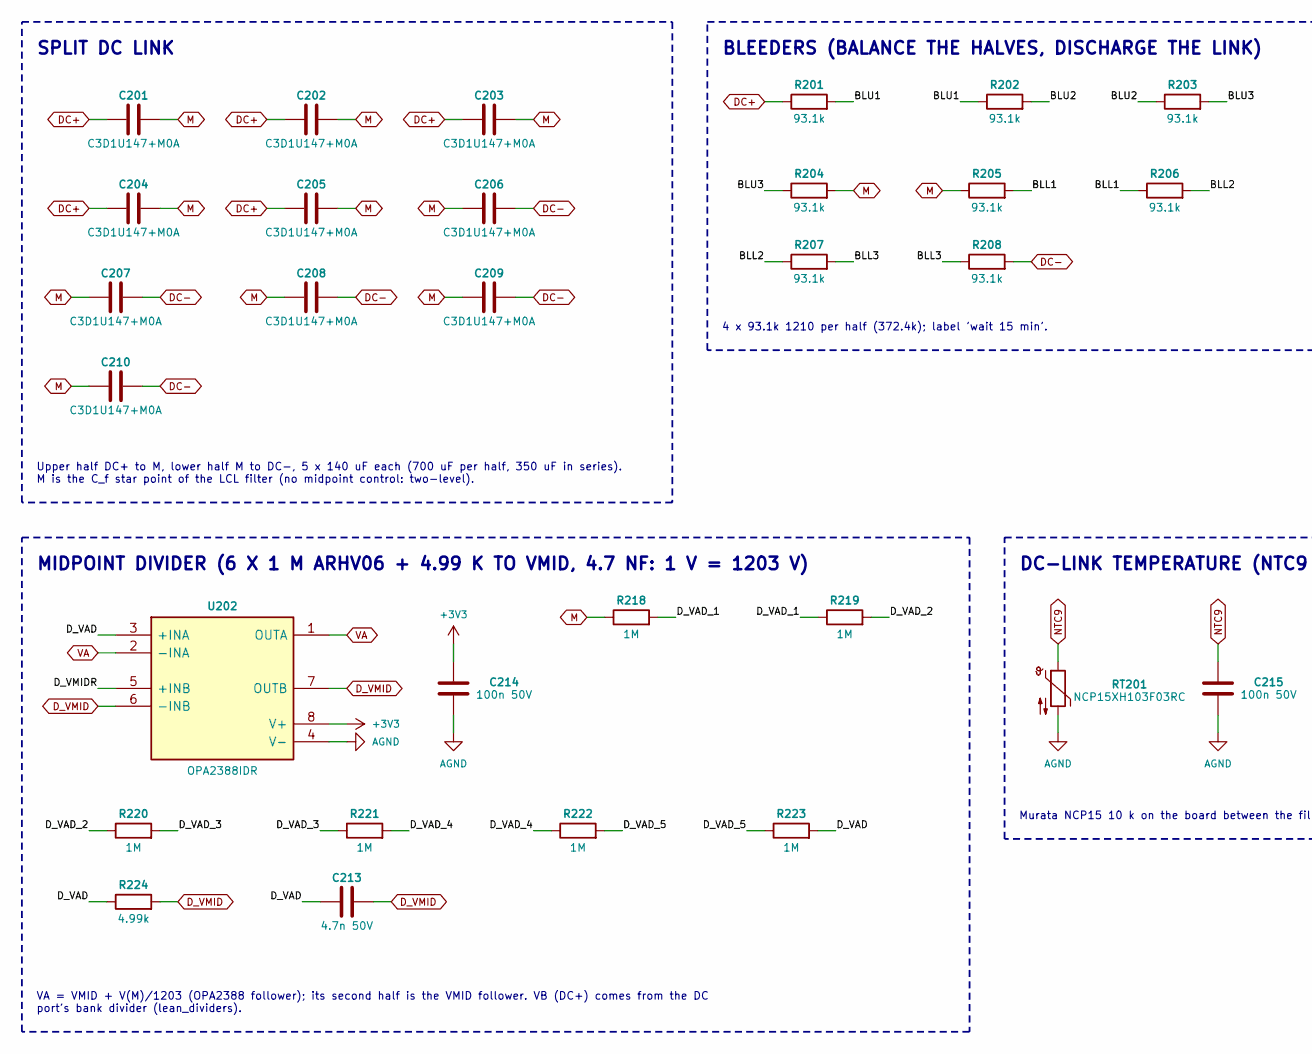
[picture p357: schematic 02_dclink.kicad_sch, part in row 1, column 1]


Parts:
C201, C202, C203, C204, C205, C206, C207, C208, C209, C210: C3D1U147+M0A; MPN C3D1U147+M0A
C211, C212, C214, C215: 100n 50V
C213: 4.7n 50V
R201, R202, R203, R204, R205, R206, R207, R208: 93.1k
R209: 11.8k
R210, R211: 1.65k
R212: 14.7k
R213: 3.57k
R214, R216: 6.04k
R215: 8.06k
R217: 6.49k
R218, R219, R220, R221, R222, R223: 1M; MPN ARHV06BTC1004A
R224: 4.99k; MPN TNPW12064K99BEEA
RT201: NCP15XH103F03RC; MPN NCP15XH103F03RC
U201: REF3030EAIDBZR; MPN REF3030EAIDBZR
U202: OPA2388IDR; MPN OPA2388IDR

Connections:
+3V3: C214.1, U202.8 (V+)
+5V: C211.1, U201.1 (IN)
AGND: C211.2, C212.2, C214.2, C215.2, R212.2, R217.2, RT201.2, U201.3 (GND), U202.4 (V-)
BLL1: R205.2, R206.1
BLL2: R206.2, R207.1
BLL3: R207.2, R208.1
BLU1: R201.2, R202.1
BLU2: R202.2, R203.1
BLU3: R203.2, R204.1
DC+: C201.1, C202.1, C203.1, C204.1, C205.1, R201.1
DC-: C206.2, C207.2, C208.2, C209.2, C210.2, R208.2
D_HOLD_HI: R213.2, R214.1
D_HOLD_LO: R216.2, R217.1
D_OC_HI: R214.2, R215.1
D_OC_LO: R215.2, R216.1
D_REF: C212.1, R209.1, R213.1, U201.2 (OUT)
D_TH_HI: R209.2, R210.1
D_TH_LO: R211.2, R212.1
D_VAD: C213.1, R223.2, R224.1, U202.3 (+INA)
D_VAD_1: R218.2, R219.1
D_VAD_2: R219.2, R220.1
D_VAD_3: R220.2, R221.1
D_VAD_4: R221.2, R222.1
D_VAD_5: R222.2, R223.1
D_VMID: C213.2, R224.2, U202.6 (-INB), U202.7 (OUTB)
D_VMIDR: R210.2, R211.1, U202.5 (+INB)
M: C201.2, C202.2, C203.2, C204.2, C205.2, C206.1, C207.1, C208.1, C209.1, C210.1, R204.2, R205.1, R218.1
NTC9: C215.1, RT201.1
VA: U202.1 (OUTA), U202.2 (-INA)

Notes on the sheet:
MIDPOINT DIVIDER (6 X 1 M ARHV06 + 4.99 K TO VMID, 4.7 NF: 1 V = 1203 V)
REFERENCE (PORT.LEAN_REFS: REF3030E, VMID 1.646 V AND THE DC-PORT THRESHOLD LADDERS)
SPLIT DC LINK
DC-LINK TEMPERATURE (NTC9 TO PCS_X)
Shared with the DC port (stage 4). VMID buffered here; IA, IA_H, VAX of PCS_PC sit on it.
VA = VMID + V(M)/1203 (OPA2388 follower); its second half is the VMID follower. VB (DC+) comes from the DC port's bank divider (lean_dividers).
Murata NCP15 10 k on the board between the film capacitors; biased on the control board.
4 x 93.1k 1210 per half (372.4k); label 'wait 15 min'.
BLEEDERS (BALANCE THE HALVES, DISCHARGE THE LINK)
Upper half DC+ to M, lower half M to DC-, 5 x 140 uF each (700 uF per half, 350 uF in series). M is the C_f star point of the LCL filter (no midpoint control: two-level).
