vectivolt/PCM/hardware/PCS-PWR/sheets/06_gdah.kicad_sch

## KiCad design hardware/PCS-PWR/sheets/06_gdah.kicad_sch (2026-10-07)

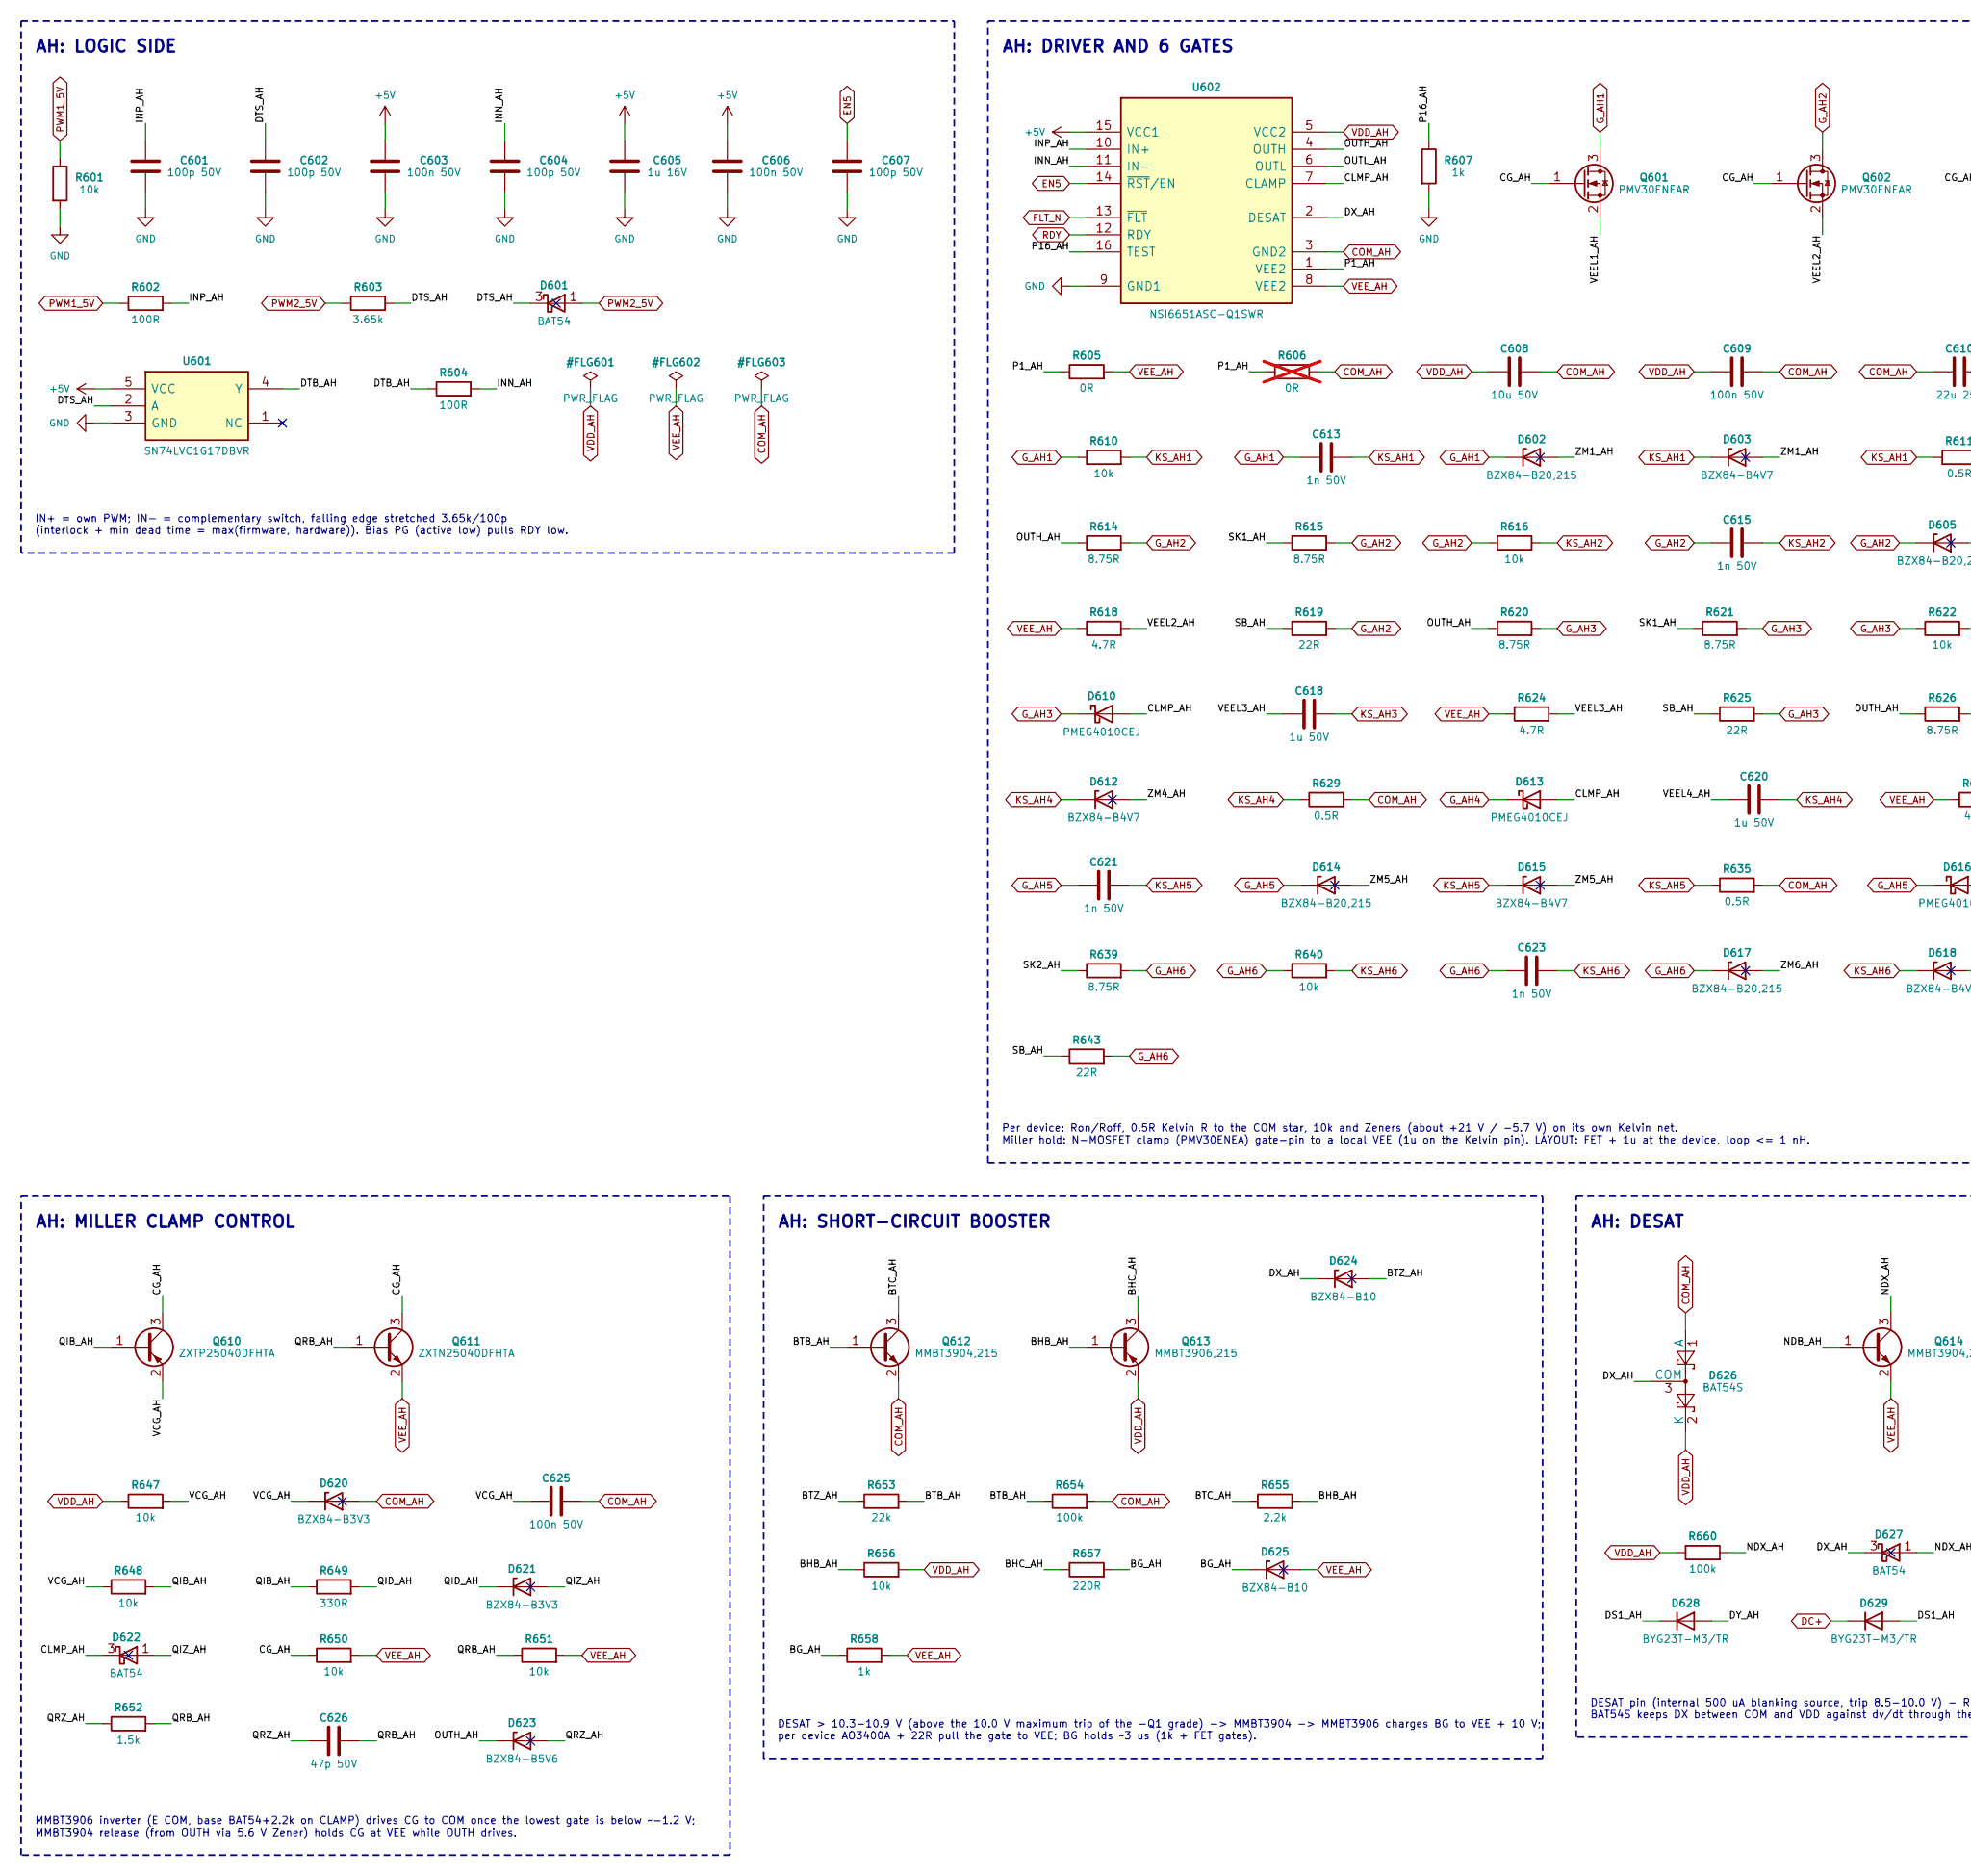
[picture p358: schematic 06_gdah.kicad_sch, part in row 1, column 1]

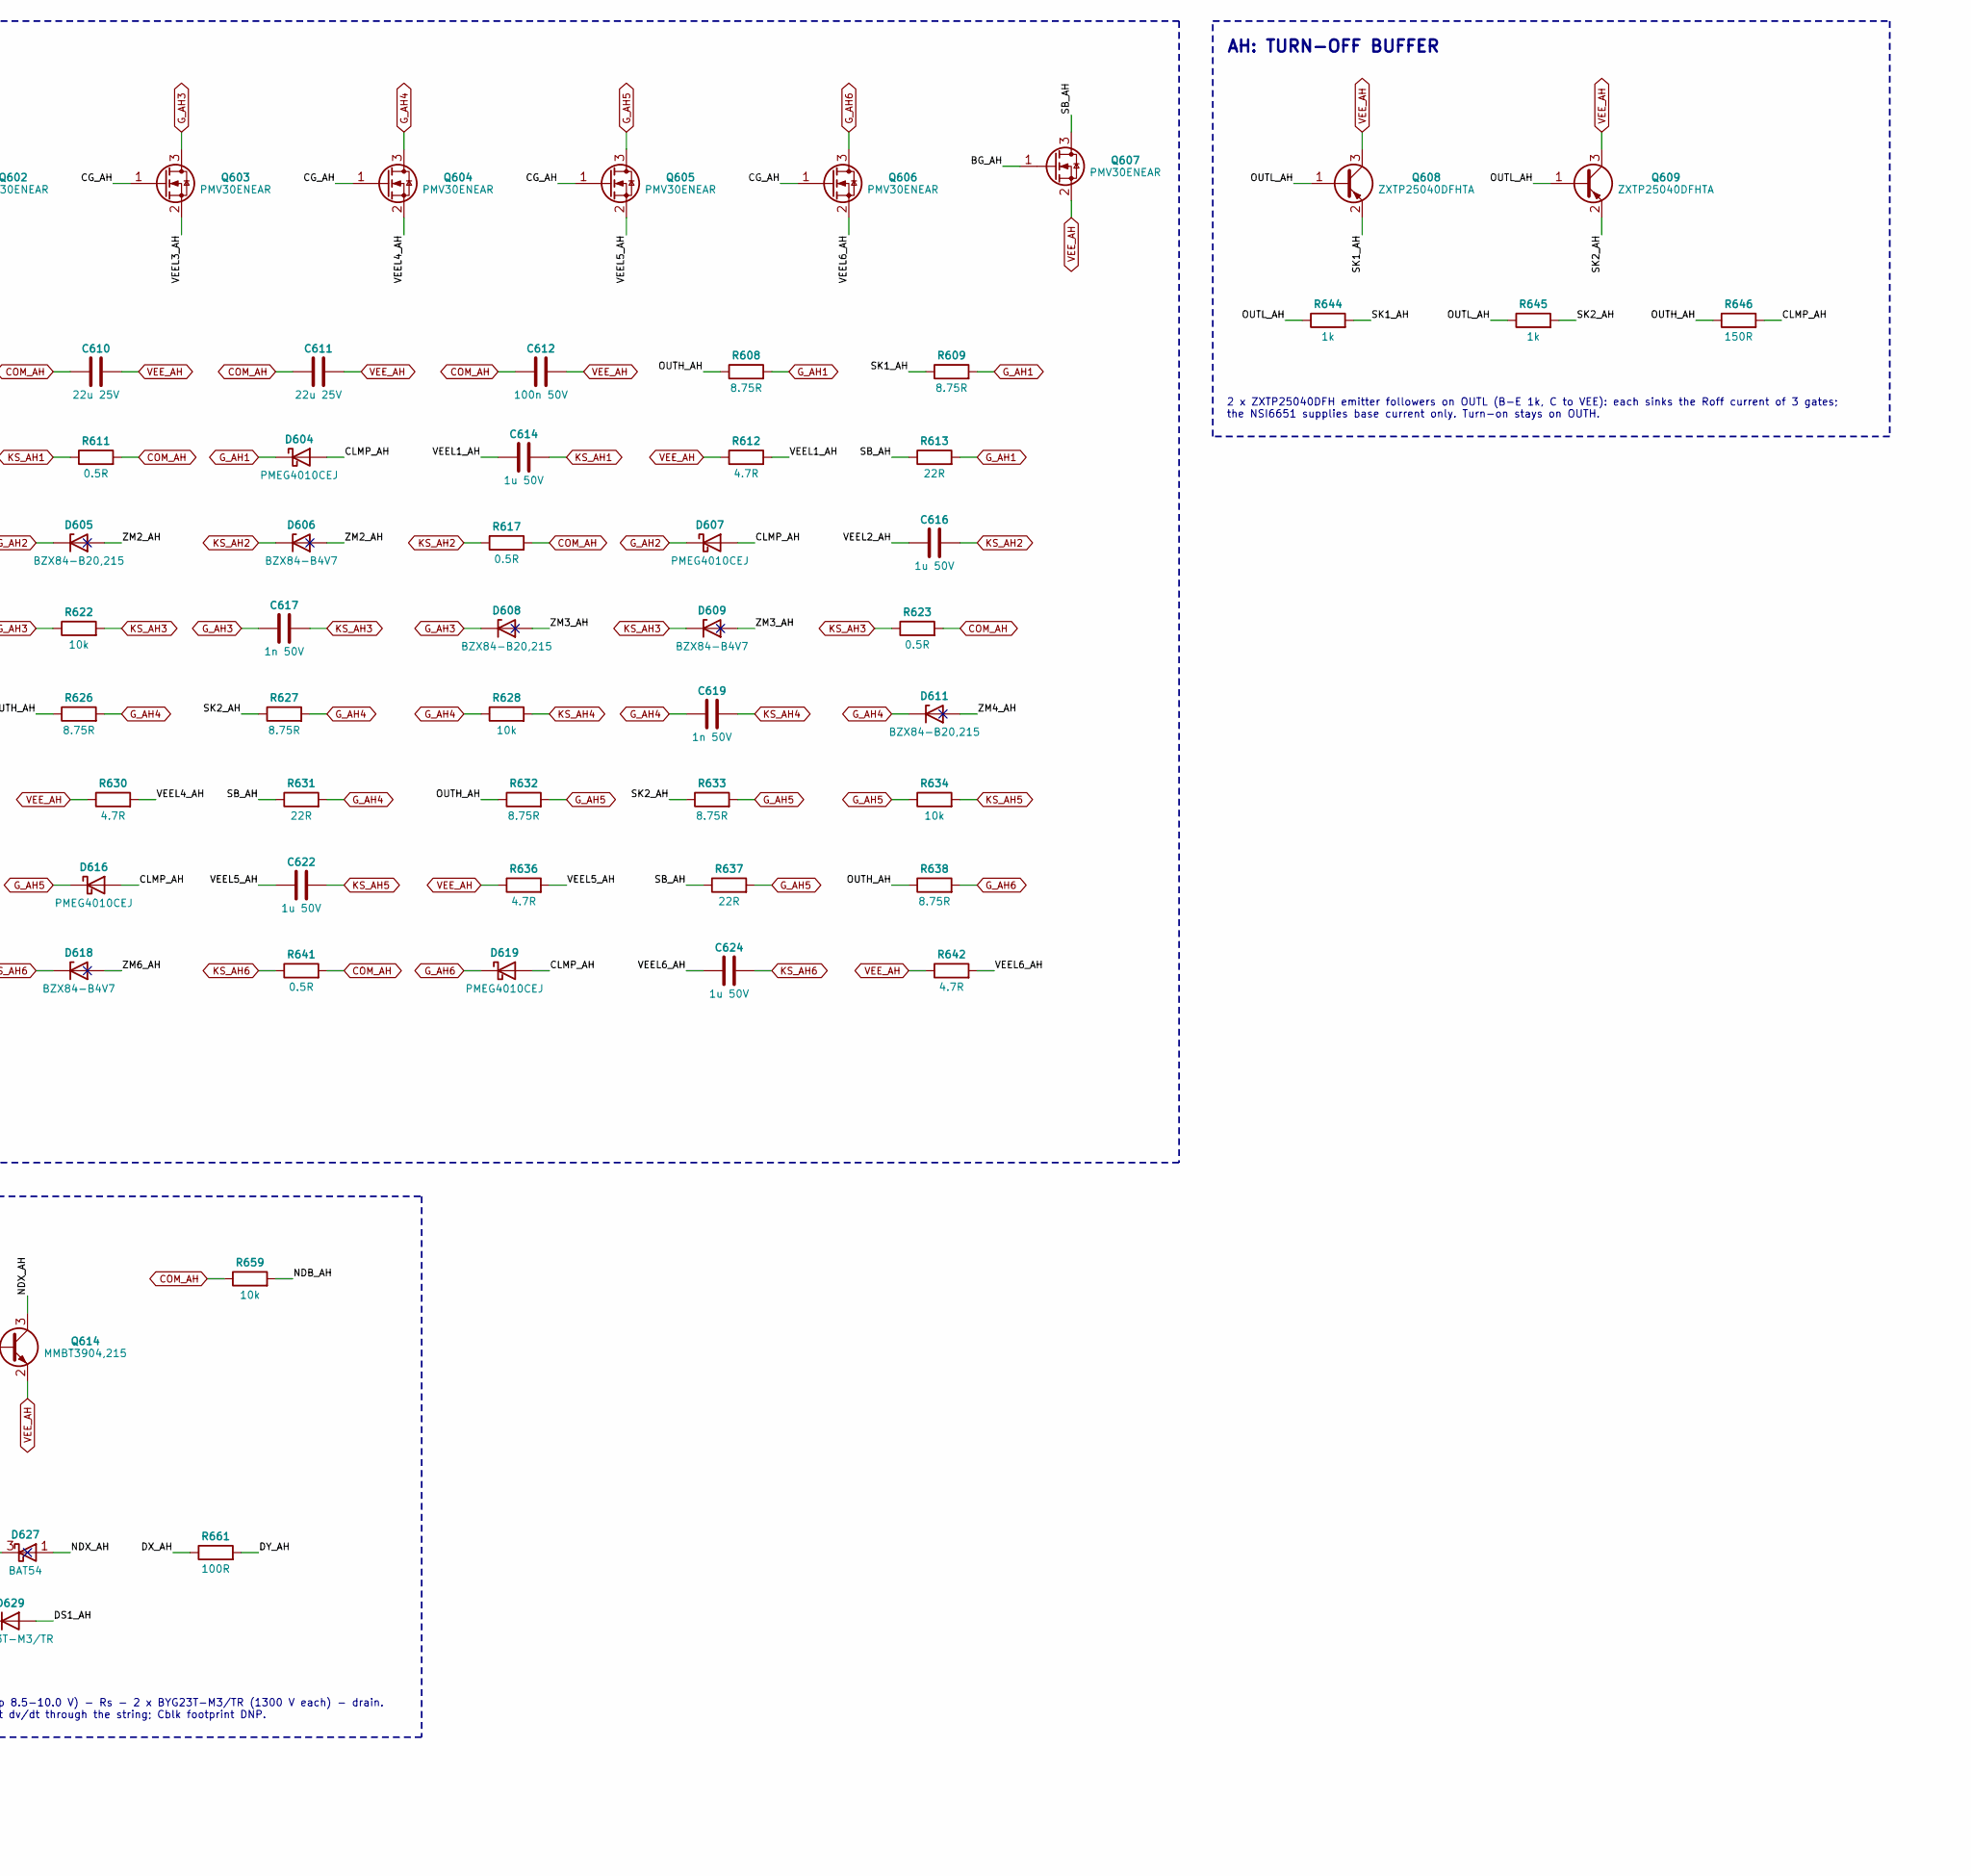
[picture p359: schematic 06_gdah.kicad_sch, part in row 1, column 2]

Parts:
C601, C602, C604, C607: 100p 50V
C603, C606, C609, C612, C625: 100n 50V
C605: 1u 16V
C608: 10u 50V
C610, C611: 22u 25V
C613, C615, C617, C619, C621, C623: 1n 50V
C614, C616, C618, C620, C622, C624: 1u 50V
C626: 47p 50V
D601, D622, D627: BAT54; MPN BAT54
D602, D605, D608, D611, D614, D617: BZX84-B20,215; MPN BZX84-B20,215
D603, D606, D609, D612, D615, D618: BZX84-B4V7; MPN BZX84-B4V7
D604, D607, D610, D613, D616, D619: PMEG4010CEJ; MPN PMEG4010CEJ
D620, D621: BZX84-B3V3; MPN BZX84-B3V3
D623: BZX84-B5V6; MPN BZX84-B5V6
D624, D625: BZX84-B10; MPN BZX84-B10
D626: BAT54S; MPN BAT54S
D628, D629: BYG23T-M3/TR; MPN BYG23T-M3/TR
Q601, Q602, Q603, Q604, Q605, Q606, Q607: PMV30ENEAR; MPN PMV30ENEAR
Q608, Q609, Q610: ZXTP25040DFHTA; MPN ZXTP25040DFHTA
Q611: ZXTN25040DFHTA; MPN ZXTN25040DFHTA
Q612, Q614: MMBT3904,215; MPN MMBT3904,215
Q613: MMBT3906,215; MPN MMBT3906,215
R601, R610, R616, R622, R628, R634, R640, R647, R648, R650, R651, R656, R659: 10k
R602, R604, R661: 100R
R603: 3.65k
R605: 0R
R606: 0R; not fitted
R607, R644, R645, R658: 1k
R608, R609, R614, R615, R620, R621, R626, R627, R632, R633, R638, R639: 8.75R
R611, R617, R623, R629, R635, R641: 0.5R
R612, R618, R624, R630, R636, R642: 4.7R
R613, R619, R625, R631, R637, R643: 22R
R646: 150R
R649: 330R
R652: 1.5k
R653: 22k
R654, R660: 100k
R655: 2.2k
R657: 220R
U601: SN74LVC1G17DBVR; MPN SN74LVC1G17DBVR
U602: NSI6651ASC-Q1SWR; MPN NSI6651ASC-Q1SWR

Connections:
+5V: C603.1, C605.1, C606.1, U601.5 (VCC), U602.15 (VCC1)
BG_AH: D625.3 (K), Q607.1 (G), R657.2, R658.1
BHB_AH: Q613.1 (B), R655.2, R656.1
BHC_AH: Q613.3 (C), R657.1
BTB_AH: Q612.1 (B), R653.2, R654.1
BTC_AH: Q612.3 (C), R655.1
BTZ_AH: D624.1 (A), R653.1
CG_AH: Q601.1 (G), Q602.1 (G), Q603.1 (G), Q604.1 (G), Q605.1 (G), Q606.1 (G), Q610.3 (C), Q611.3 (C), R650.1
CLMP_AH: D604.2 (A), D607.2 (A), D610.2 (A), D613.2 (A), D616.2 (A), D619.2 (A), D622.3 (K), R646.2, U602.7 (CLAMP)
COM_AH: C608.2, C609.2, C610.1, C611.1, C612.1, C625.2, D620.1 (A), D626.1 (A), Q612.2 (E), R606.2, R611.2, R617.2, R623.2, R629.2, R635.2, R641.2, R654.2, R659.1, U602.3 (GND2)
DC+: D629.1 (K)
DS1_AH: D628.1 (K), D629.2 (A)
DTB_AH: R604.1, U601.4 (Y)
DTS_AH: C602.1, D601.3 (K), R603.2, U601.2 (A)
DX_AH: D624.3 (K), D626.3 (COM), D627.3 (K), R661.1, U602.2 (DESAT)
DY_AH: D628.2 (A), R661.2
EN5: C607.1, U602.14 (~RST/EN)
FLT_N: U602.13 (~FLT)
GND: C601.2, C602.2, C603.2, C604.2, C605.2, C606.2, C607.2, R601.2, R607.2, U601.3 (GND), U602.9 (GND1)
G_AH1: C613.1, D602.3 (K), D604.1 (K), Q601.3 (D), R608.2, R609.2, R610.1, R613.2
G_AH2: C615.1, D605.3 (K), D607.1 (K), Q602.3 (D), R614.2, R615.2, R616.1, R619.2
G_AH3: C617.1, D608.3 (K), D610.1 (K), Q603.3 (D), R620.2, R621.2, R622.1, R625.2
G_AH4: C619.1, D611.3 (K), D613.1 (K), Q604.3 (D), R626.2, R627.2, R628.1, R631.2
G_AH5: C621.1, D614.3 (K), D616.1 (K), Q605.3 (D), R632.2, R633.2, R634.1, R637.2
G_AH6: C623.1, D617.3 (K), D619.1 (K), Q606.3 (D), R638.2, R639.2, R640.1, R643.2
INN_AH: C604.1, R604.2, U602.11 (IN-)
INP_AH: C601.1, R602.2, U602.10 (IN+)
KS_AH1: C613.2, C614.2, D603.3 (K), R610.2, R611.1
KS_AH2: C615.2, C616.2, D606.3 (K), R616.2, R617.1
KS_AH3: C617.2, C618.2, D609.3 (K), R622.2, R623.1
KS_AH4: C619.2, C620.2, D612.3 (K), R628.2, R629.1
KS_AH5: C621.2, C622.2, D615.3 (K), R634.2, R635.1
KS_AH6: C623.2, C624.2, D618.3 (K), R640.2, R641.1
NDB_AH: Q614.1 (B), R659.2
NDX_AH: D627.1 (A), Q614.3 (C), R660.2
OUTH_AH: D623.3 (K), R608.1, R614.1, R620.1, R626.1, R632.1, R638.1, R646.1, U602.4 (OUTH)
OUTL_AH: Q608.1 (B), Q609.1 (B), R644.1, R645.1, U602.6 (OUTL)
P1_AH: R605.1, R606.1, U602.1 (VEE2)
P16_AH: R607.1, U602.16 (TEST)
PWM1_5V: R601.1, R602.1
PWM2_5V: D601.1 (A), R603.1
QIB_AH: Q610.1 (B), R648.2, R649.1
QID_AH: D621.3 (K), R649.2
QIZ_AH: D621.1 (A), D622.1 (A)
QRB_AH: C626.2, Q611.1 (B), R651.1, R652.2
QRZ_AH: C626.1, D623.1 (A), R652.1
RDY: U602.12 (RDY)
SB_AH: Q607.3 (D), R613.1, R619.1, R625.1, R631.1, R637.1, R643.1
SK1_AH: Q608.2 (E), R609.1, R615.1, R621.1, R644.2
SK2_AH: Q609.2 (E), R627.1, R633.1, R639.1, R645.2
VCG_AH: C625.1, D620.3 (K), Q610.2 (E), R647.2, R648.1
VDD_AH: C608.1, C609.1, D626.2 (K), Q613.2 (E), R647.1, R656.2, R660.1, U602.5 (VCC2)
VEEL1_AH: C614.1, Q601.2 (S), R612.2
VEEL2_AH: C616.1, Q602.2 (S), R618.2
VEEL3_AH: C618.1, Q603.2 (S), R624.2
VEEL4_AH: C620.1, Q604.2 (S), R630.2
VEEL5_AH: C622.1, Q605.2 (S), R636.2
VEEL6_AH: C624.1, Q606.2 (S), R642.2
VEE_AH: C610.2, C611.2, C612.2, D625.1 (A), Q607.2 (S), Q608.3 (C), Q609.3 (C), Q611.2 (E), Q614.2 (E), R605.2, R612.1, R618.1, R624.1, R630.1, R636.1, R642.1, R650.2, R651.2, R658.2, U602.8 (VEE2)
ZM1_AH: D602.1 (A), D603.1 (A)
ZM2_AH: D605.1 (A), D606.1 (A)
ZM3_AH: D608.1 (A), D609.1 (A)
ZM4_AH: D611.1 (A), D612.1 (A)
ZM5_AH: D614.1 (A), D615.1 (A)
ZM6_AH: D617.1 (A), D618.1 (A)

Notes on the sheet:
DESAT > 10.3-10.9 V (above the 10.0 V maximum trip of the -Q1 grade) -> MMBT3904 -> MMBT3906 charges BG to VEE + 10 V; per device AO3400A + 22R pull the gate to VEE; BG holds ~3 us (1k + FET gates).
AH: DRIVER AND 6 GATES
AH: TURN-OFF BUFFER
AH: MILLER CLAMP CONTROL
2 x ZXTP25040DFH emitter followers on OUTL (B-E 1k, C to VEE): each sinks the Roff current of 3 gates; the NSI6651 supplies base current only. Turn-on stays on OUTH.
MMBT3906 inverter (E COM, base BAT54+2.2k on CLAMP) drives CG to COM once the lowest gate is below ~-1.2 V; MMBT3904 release (from OUTH via 5.6 V Zener) holds CG at VEE while OUTH drives.
DESAT pin (internal 500 uA blanking source, trip 8.5-10.0 V) - Rs - 2 x BYG23T-M3/TR (1300 V each) - drain. BAT54S keeps DX between COM and VDD against dv/dt through the string; Cblk footprint DNP.
AH: SHORT-CIRCUIT BOOSTER
Per device: Ron/Roff, 0.5R Kelvin R to the COM star, 10k and Zeners (about +21 V / -5.7 V) on its own Kelvin net. Miller hold: N-MOSFET clamp (PMV30ENEA) gate-pin to a local VEE (1u on the Kelvin pin). LAYOUT: FET + 1u at the device, loop <= 1 nH.
AH: LOGIC SIDE
IN+ = own PWM; IN- = complementary switch, falling edge stretched 3.65k/100p (interlock + min dead time = max(firmware, hardware)). Bias PG (active low) pulls RDY low.
AH: DESAT
