vectivolt/PCM/hardware/PCS-PWR/sheets/08_gdbh.kicad_sch

## KiCad design hardware/PCS-PWR/sheets/08_gdbh.kicad_sch (2026-10-07)

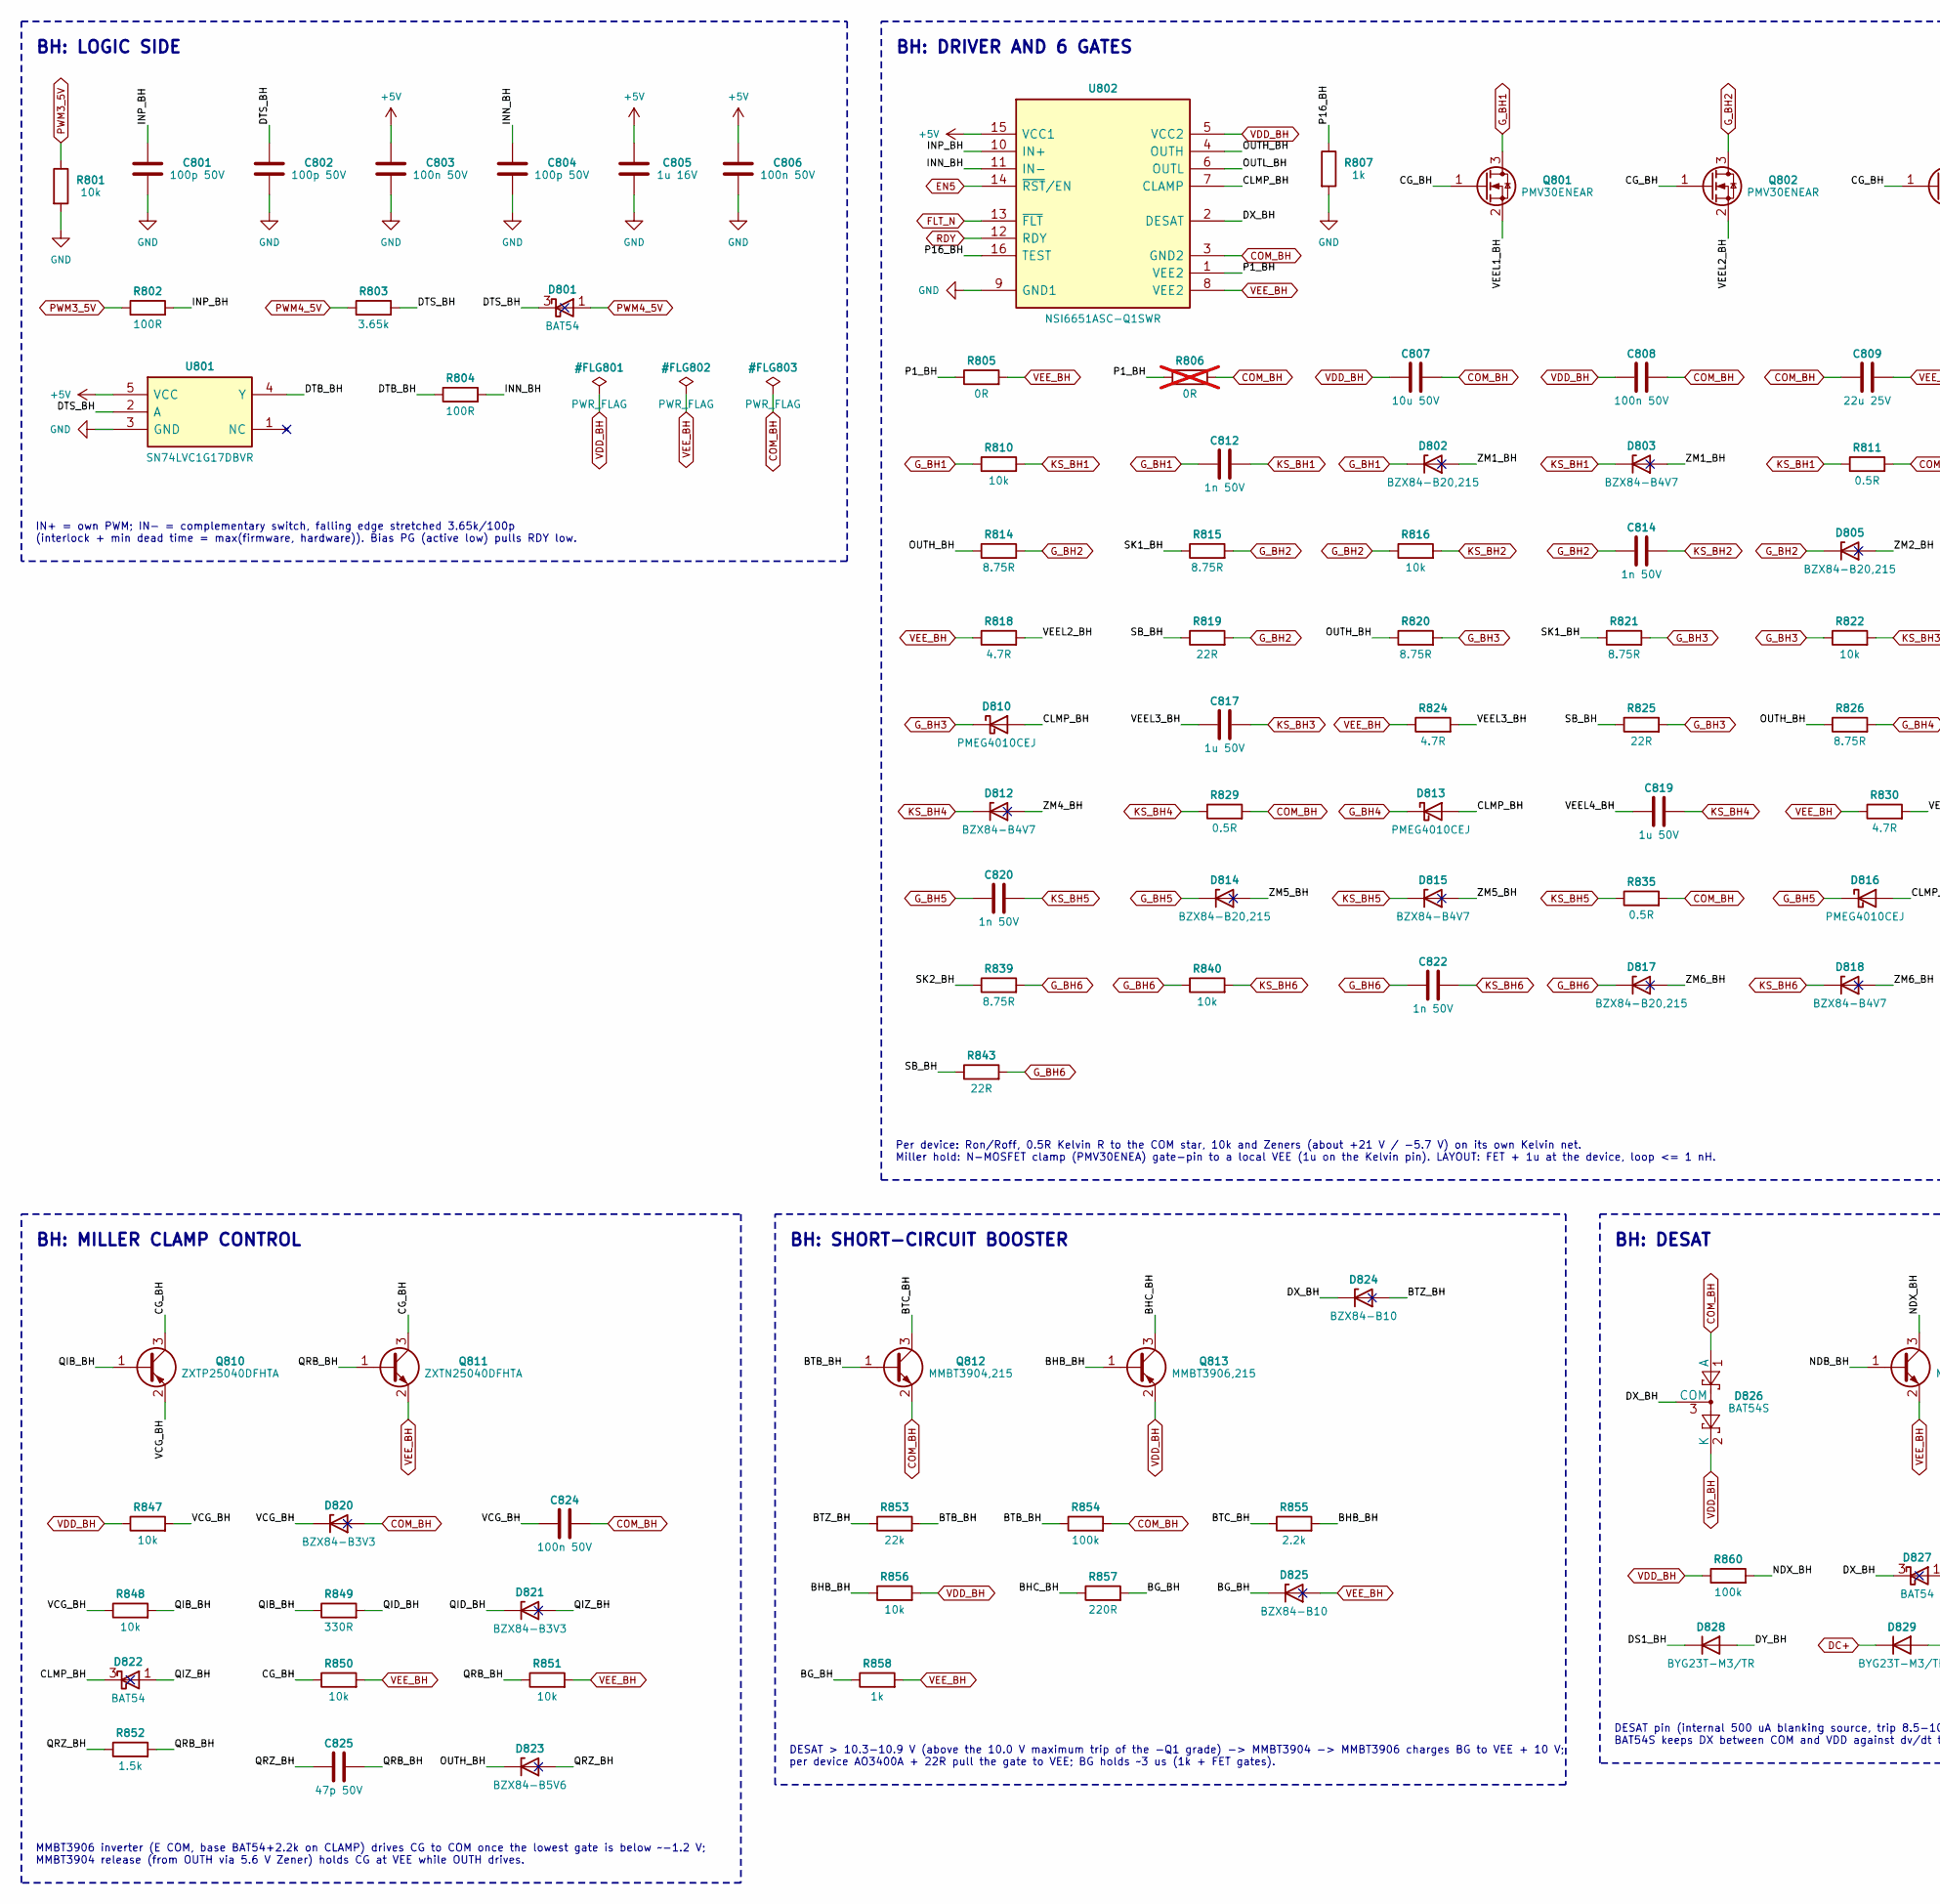
[picture p363: schematic 08_gdbh.kicad_sch, part in row 1, column 1]

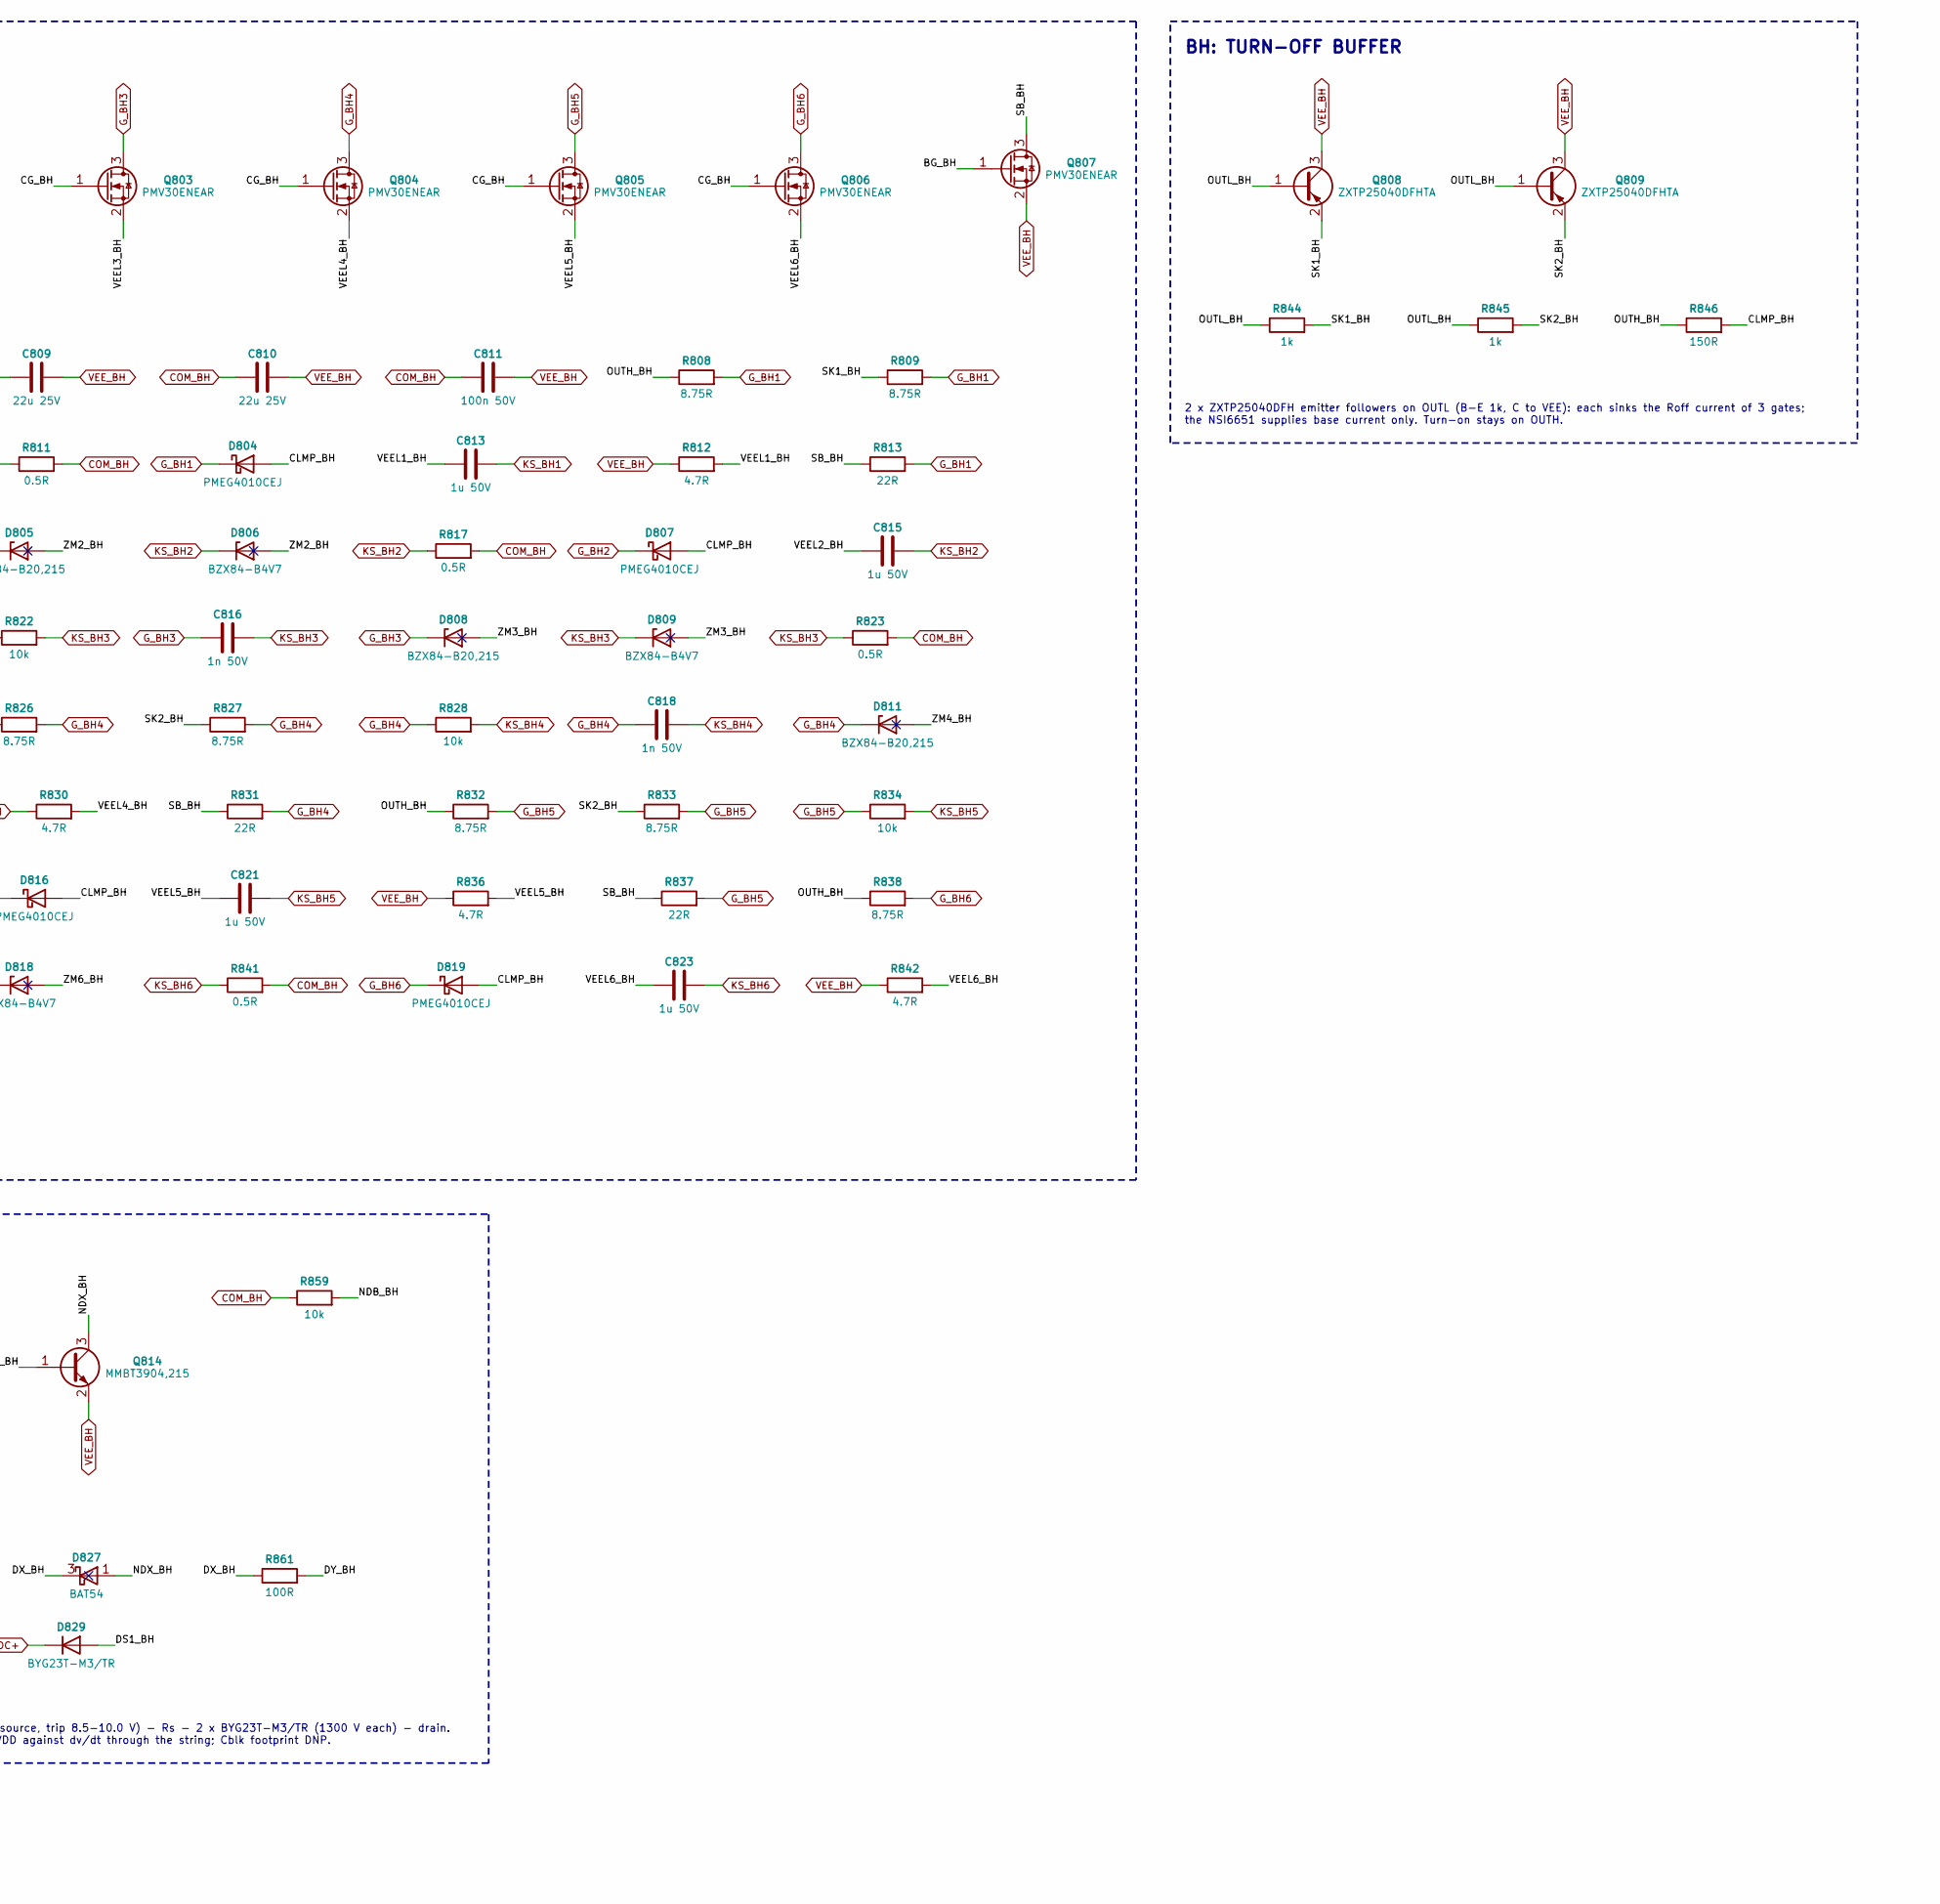
[picture p364: schematic 08_gdbh.kicad_sch, part in row 1, column 2]

Parts:
C801, C802, C804: 100p 50V
C803, C806, C808, C811, C824: 100n 50V
C805: 1u 16V
C807: 10u 50V
C809, C810: 22u 25V
C812, C814, C816, C818, C820, C822: 1n 50V
C813, C815, C817, C819, C821, C823: 1u 50V
C825: 47p 50V
D801, D822, D827: BAT54; MPN BAT54
D802, D805, D808, D811, D814, D817: BZX84-B20,215; MPN BZX84-B20,215
D803, D806, D809, D812, D815, D818: BZX84-B4V7; MPN BZX84-B4V7
D804, D807, D810, D813, D816, D819: PMEG4010CEJ; MPN PMEG4010CEJ
D820, D821: BZX84-B3V3; MPN BZX84-B3V3
D823: BZX84-B5V6; MPN BZX84-B5V6
D824, D825: BZX84-B10; MPN BZX84-B10
D826: BAT54S; MPN BAT54S
D828, D829: BYG23T-M3/TR; MPN BYG23T-M3/TR
Q801, Q802, Q803, Q804, Q805, Q806, Q807: PMV30ENEAR; MPN PMV30ENEAR
Q808, Q809, Q810: ZXTP25040DFHTA; MPN ZXTP25040DFHTA
Q811: ZXTN25040DFHTA; MPN ZXTN25040DFHTA
Q812, Q814: MMBT3904,215; MPN MMBT3904,215
Q813: MMBT3906,215; MPN MMBT3906,215
R801, R810, R816, R822, R828, R834, R840, R847, R848, R850, R851, R856, R859: 10k
R802, R804, R861: 100R
R803: 3.65k
R805: 0R
R806: 0R; not fitted
R807, R844, R845, R858: 1k
R808, R809, R814, R815, R820, R821, R826, R827, R832, R833, R838, R839: 8.75R
R811, R817, R823, R829, R835, R841: 0.5R
R812, R818, R824, R830, R836, R842: 4.7R
R813, R819, R825, R831, R837, R843: 22R
R846: 150R
R849: 330R
R852: 1.5k
R853: 22k
R854, R860: 100k
R855: 2.2k
R857: 220R
U801: SN74LVC1G17DBVR; MPN SN74LVC1G17DBVR
U802: NSI6651ASC-Q1SWR; MPN NSI6651ASC-Q1SWR

Connections:
+5V: C803.1, C805.1, C806.1, U801.5 (VCC), U802.15 (VCC1)
BG_BH: D825.3 (K), Q807.1 (G), R857.2, R858.1
BHB_BH: Q813.1 (B), R855.2, R856.1
BHC_BH: Q813.3 (C), R857.1
BTB_BH: Q812.1 (B), R853.2, R854.1
BTC_BH: Q812.3 (C), R855.1
BTZ_BH: D824.1 (A), R853.1
CG_BH: Q801.1 (G), Q802.1 (G), Q803.1 (G), Q804.1 (G), Q805.1 (G), Q806.1 (G), Q810.3 (C), Q811.3 (C), R850.1
CLMP_BH: D804.2 (A), D807.2 (A), D810.2 (A), D813.2 (A), D816.2 (A), D819.2 (A), D822.3 (K), R846.2, U802.7 (CLAMP)
COM_BH: C807.2, C808.2, C809.1, C810.1, C811.1, C824.2, D820.1 (A), D826.1 (A), Q812.2 (E), R806.2, R811.2, R817.2, R823.2, R829.2, R835.2, R841.2, R854.2, R859.1, U802.3 (GND2)
DC+: D829.1 (K)
DS1_BH: D828.1 (K), D829.2 (A)
DTB_BH: R804.1, U801.4 (Y)
DTS_BH: C802.1, D801.3 (K), R803.2, U801.2 (A)
DX_BH: D824.3 (K), D826.3 (COM), D827.3 (K), R861.1, U802.2 (DESAT)
DY_BH: D828.2 (A), R861.2
EN5: U802.14 (~RST/EN)
FLT_N: U802.13 (~FLT)
GND: C801.2, C802.2, C803.2, C804.2, C805.2, C806.2, R801.2, R807.2, U801.3 (GND), U802.9 (GND1)
G_BH1: C812.1, D802.3 (K), D804.1 (K), Q801.3 (D), R808.2, R809.2, R810.1, R813.2
G_BH2: C814.1, D805.3 (K), D807.1 (K), Q802.3 (D), R814.2, R815.2, R816.1, R819.2
G_BH3: C816.1, D808.3 (K), D810.1 (K), Q803.3 (D), R820.2, R821.2, R822.1, R825.2
G_BH4: C818.1, D811.3 (K), D813.1 (K), Q804.3 (D), R826.2, R827.2, R828.1, R831.2
G_BH5: C820.1, D814.3 (K), D816.1 (K), Q805.3 (D), R832.2, R833.2, R834.1, R837.2
G_BH6: C822.1, D817.3 (K), D819.1 (K), Q806.3 (D), R838.2, R839.2, R840.1, R843.2
INN_BH: C804.1, R804.2, U802.11 (IN-)
INP_BH: C801.1, R802.2, U802.10 (IN+)
KS_BH1: C812.2, C813.2, D803.3 (K), R810.2, R811.1
KS_BH2: C814.2, C815.2, D806.3 (K), R816.2, R817.1
KS_BH3: C816.2, C817.2, D809.3 (K), R822.2, R823.1
KS_BH4: C818.2, C819.2, D812.3 (K), R828.2, R829.1
KS_BH5: C820.2, C821.2, D815.3 (K), R834.2, R835.1
KS_BH6: C822.2, C823.2, D818.3 (K), R840.2, R841.1
NDB_BH: Q814.1 (B), R859.2
NDX_BH: D827.1 (A), Q814.3 (C), R860.2
OUTH_BH: D823.3 (K), R808.1, R814.1, R820.1, R826.1, R832.1, R838.1, R846.1, U802.4 (OUTH)
OUTL_BH: Q808.1 (B), Q809.1 (B), R844.1, R845.1, U802.6 (OUTL)
P1_BH: R805.1, R806.1, U802.1 (VEE2)
P16_BH: R807.1, U802.16 (TEST)
PWM3_5V: R801.1, R802.1
PWM4_5V: D801.1 (A), R803.1
QIB_BH: Q810.1 (B), R848.2, R849.1
QID_BH: D821.3 (K), R849.2
QIZ_BH: D821.1 (A), D822.1 (A)
QRB_BH: C825.2, Q811.1 (B), R851.1, R852.2
QRZ_BH: C825.1, D823.1 (A), R852.1
RDY: U802.12 (RDY)
SB_BH: Q807.3 (D), R813.1, R819.1, R825.1, R831.1, R837.1, R843.1
SK1_BH: Q808.2 (E), R809.1, R815.1, R821.1, R844.2
SK2_BH: Q809.2 (E), R827.1, R833.1, R839.1, R845.2
VCG_BH: C824.1, D820.3 (K), Q810.2 (E), R847.2, R848.1
VDD_BH: C807.1, C808.1, D826.2 (K), Q813.2 (E), R847.1, R856.2, R860.1, U802.5 (VCC2)
VEEL1_BH: C813.1, Q801.2 (S), R812.2
VEEL2_BH: C815.1, Q802.2 (S), R818.2
VEEL3_BH: C817.1, Q803.2 (S), R824.2
VEEL4_BH: C819.1, Q804.2 (S), R830.2
VEEL5_BH: C821.1, Q805.2 (S), R836.2
VEEL6_BH: C823.1, Q806.2 (S), R842.2
VEE_BH: C809.2, C810.2, C811.2, D825.1 (A), Q807.2 (S), Q808.3 (C), Q809.3 (C), Q811.2 (E), Q814.2 (E), R805.2, R812.1, R818.1, R824.1, R830.1, R836.1, R842.1, R850.2, R851.2, R858.2, U802.8 (VEE2)
ZM1_BH: D802.1 (A), D803.1 (A)
ZM2_BH: D805.1 (A), D806.1 (A)
ZM3_BH: D808.1 (A), D809.1 (A)
ZM4_BH: D811.1 (A), D812.1 (A)
ZM5_BH: D814.1 (A), D815.1 (A)
ZM6_BH: D817.1 (A), D818.1 (A)

Notes on the sheet:
Per device: Ron/Roff, 0.5R Kelvin R to the COM star, 10k and Zeners (about +21 V / -5.7 V) on its own Kelvin net. Miller hold: N-MOSFET clamp (PMV30ENEA) gate-pin to a local VEE (1u on the Kelvin pin). LAYOUT: FET + 1u at the device, loop <= 1 nH.
2 x ZXTP25040DFH emitter followers on OUTL (B-E 1k, C to VEE): each sinks the Roff current of 3 gates; the NSI6651 supplies base current only. Turn-on stays on OUTH.
BH: MILLER CLAMP CONTROL
DESAT pin (internal 500 uA blanking source, trip 8.5-10.0 V) - Rs - 2 x BYG23T-M3/TR (1300 V each) - drain. BAT54S keeps DX between COM and VDD against dv/dt through the string; Cblk footprint DNP.
MMBT3906 inverter (E COM, base BAT54+2.2k on CLAMP) drives CG to COM once the lowest gate is below ~-1.2 V; MMBT3904 release (from OUTH via 5.6 V Zener) holds CG at VEE while OUTH drives.
DESAT > 10.3-10.9 V (above the 10.0 V maximum trip of the -Q1 grade) -> MMBT3904 -> MMBT3906 charges BG to VEE + 10 V; per device AO3400A + 22R pull the gate to VEE; BG holds ~3 us (1k + FET gates).
BH: DRIVER AND 6 GATES
BH: DESAT
BH: SHORT-CIRCUIT BOOSTER
BH: LOGIC SIDE
IN+ = own PWM; IN- = complementary switch, falling edge stretched 3.65k/100p (interlock + min dead time = max(firmware, hardware)). Bias PG (active low) pulls RDY low.
BH: TURN-OFF BUFFER
