vectivolt/PCM/hardware/PCS-PWR/sheets/09_gdbl.kicad_sch

## KiCad design hardware/PCS-PWR/sheets/09_gdbl.kicad_sch (2026-10-07)

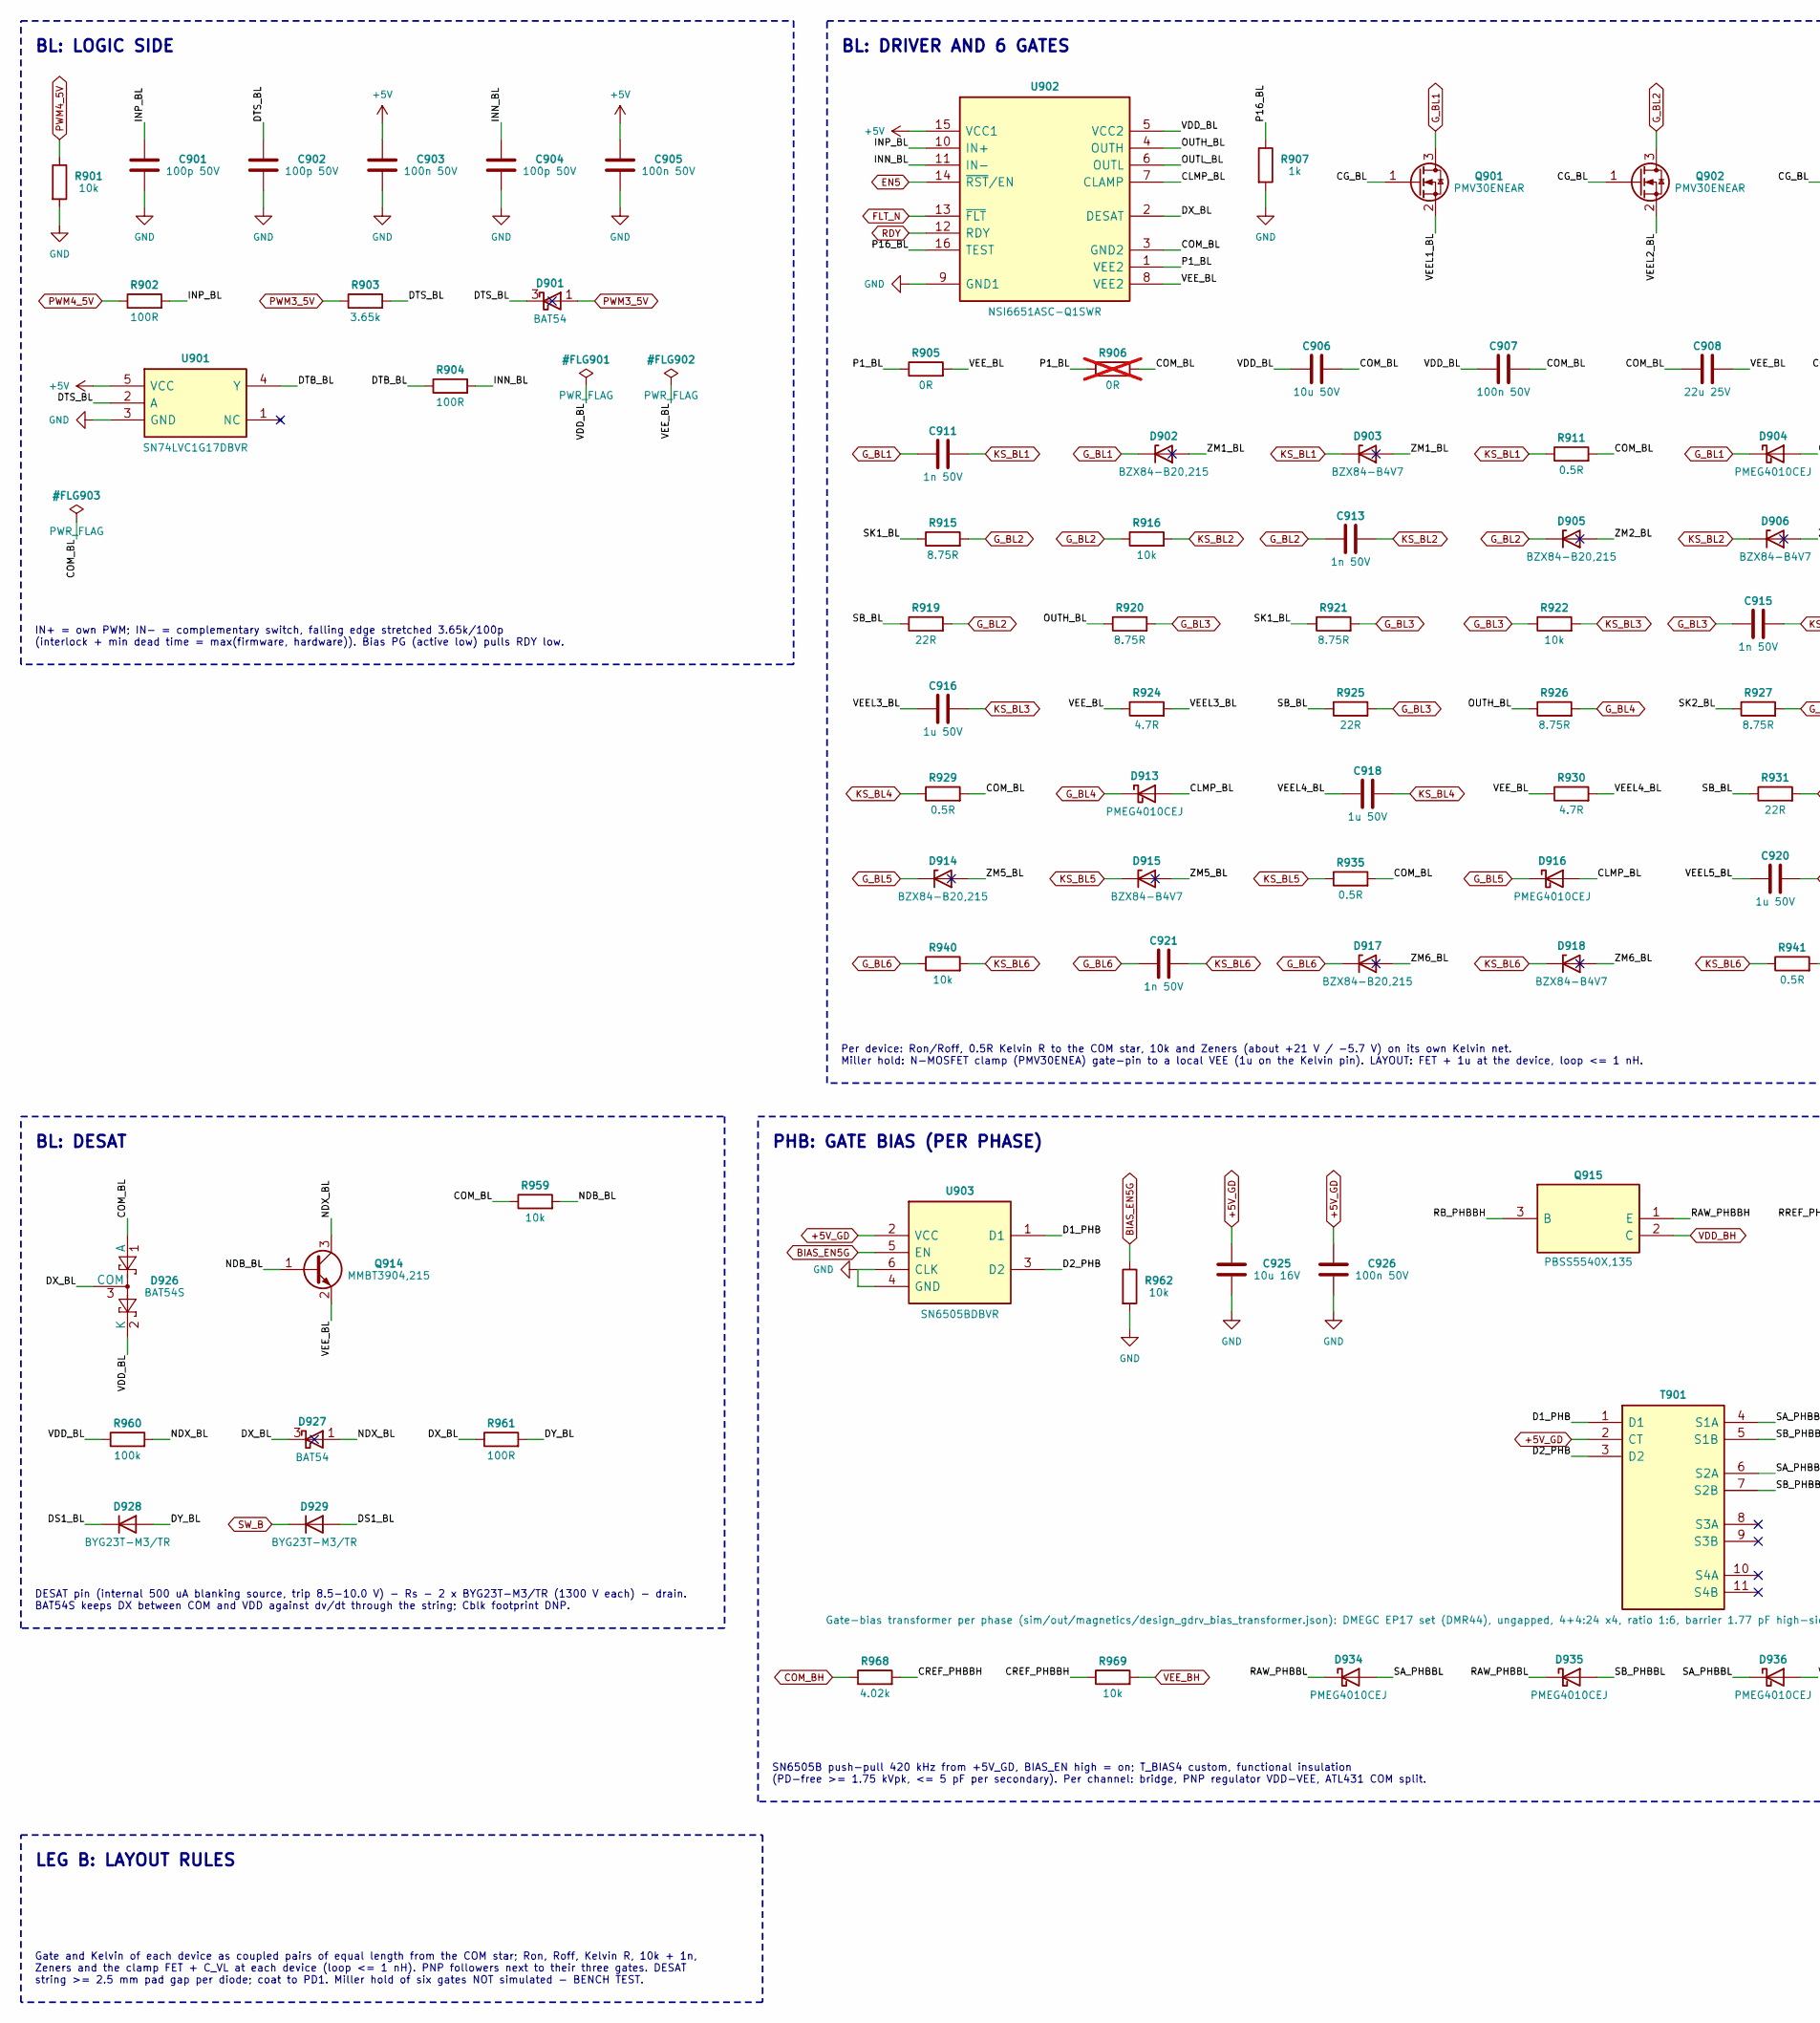
[picture p365: schematic 09_gdbl.kicad_sch, part in row 1, column 1]

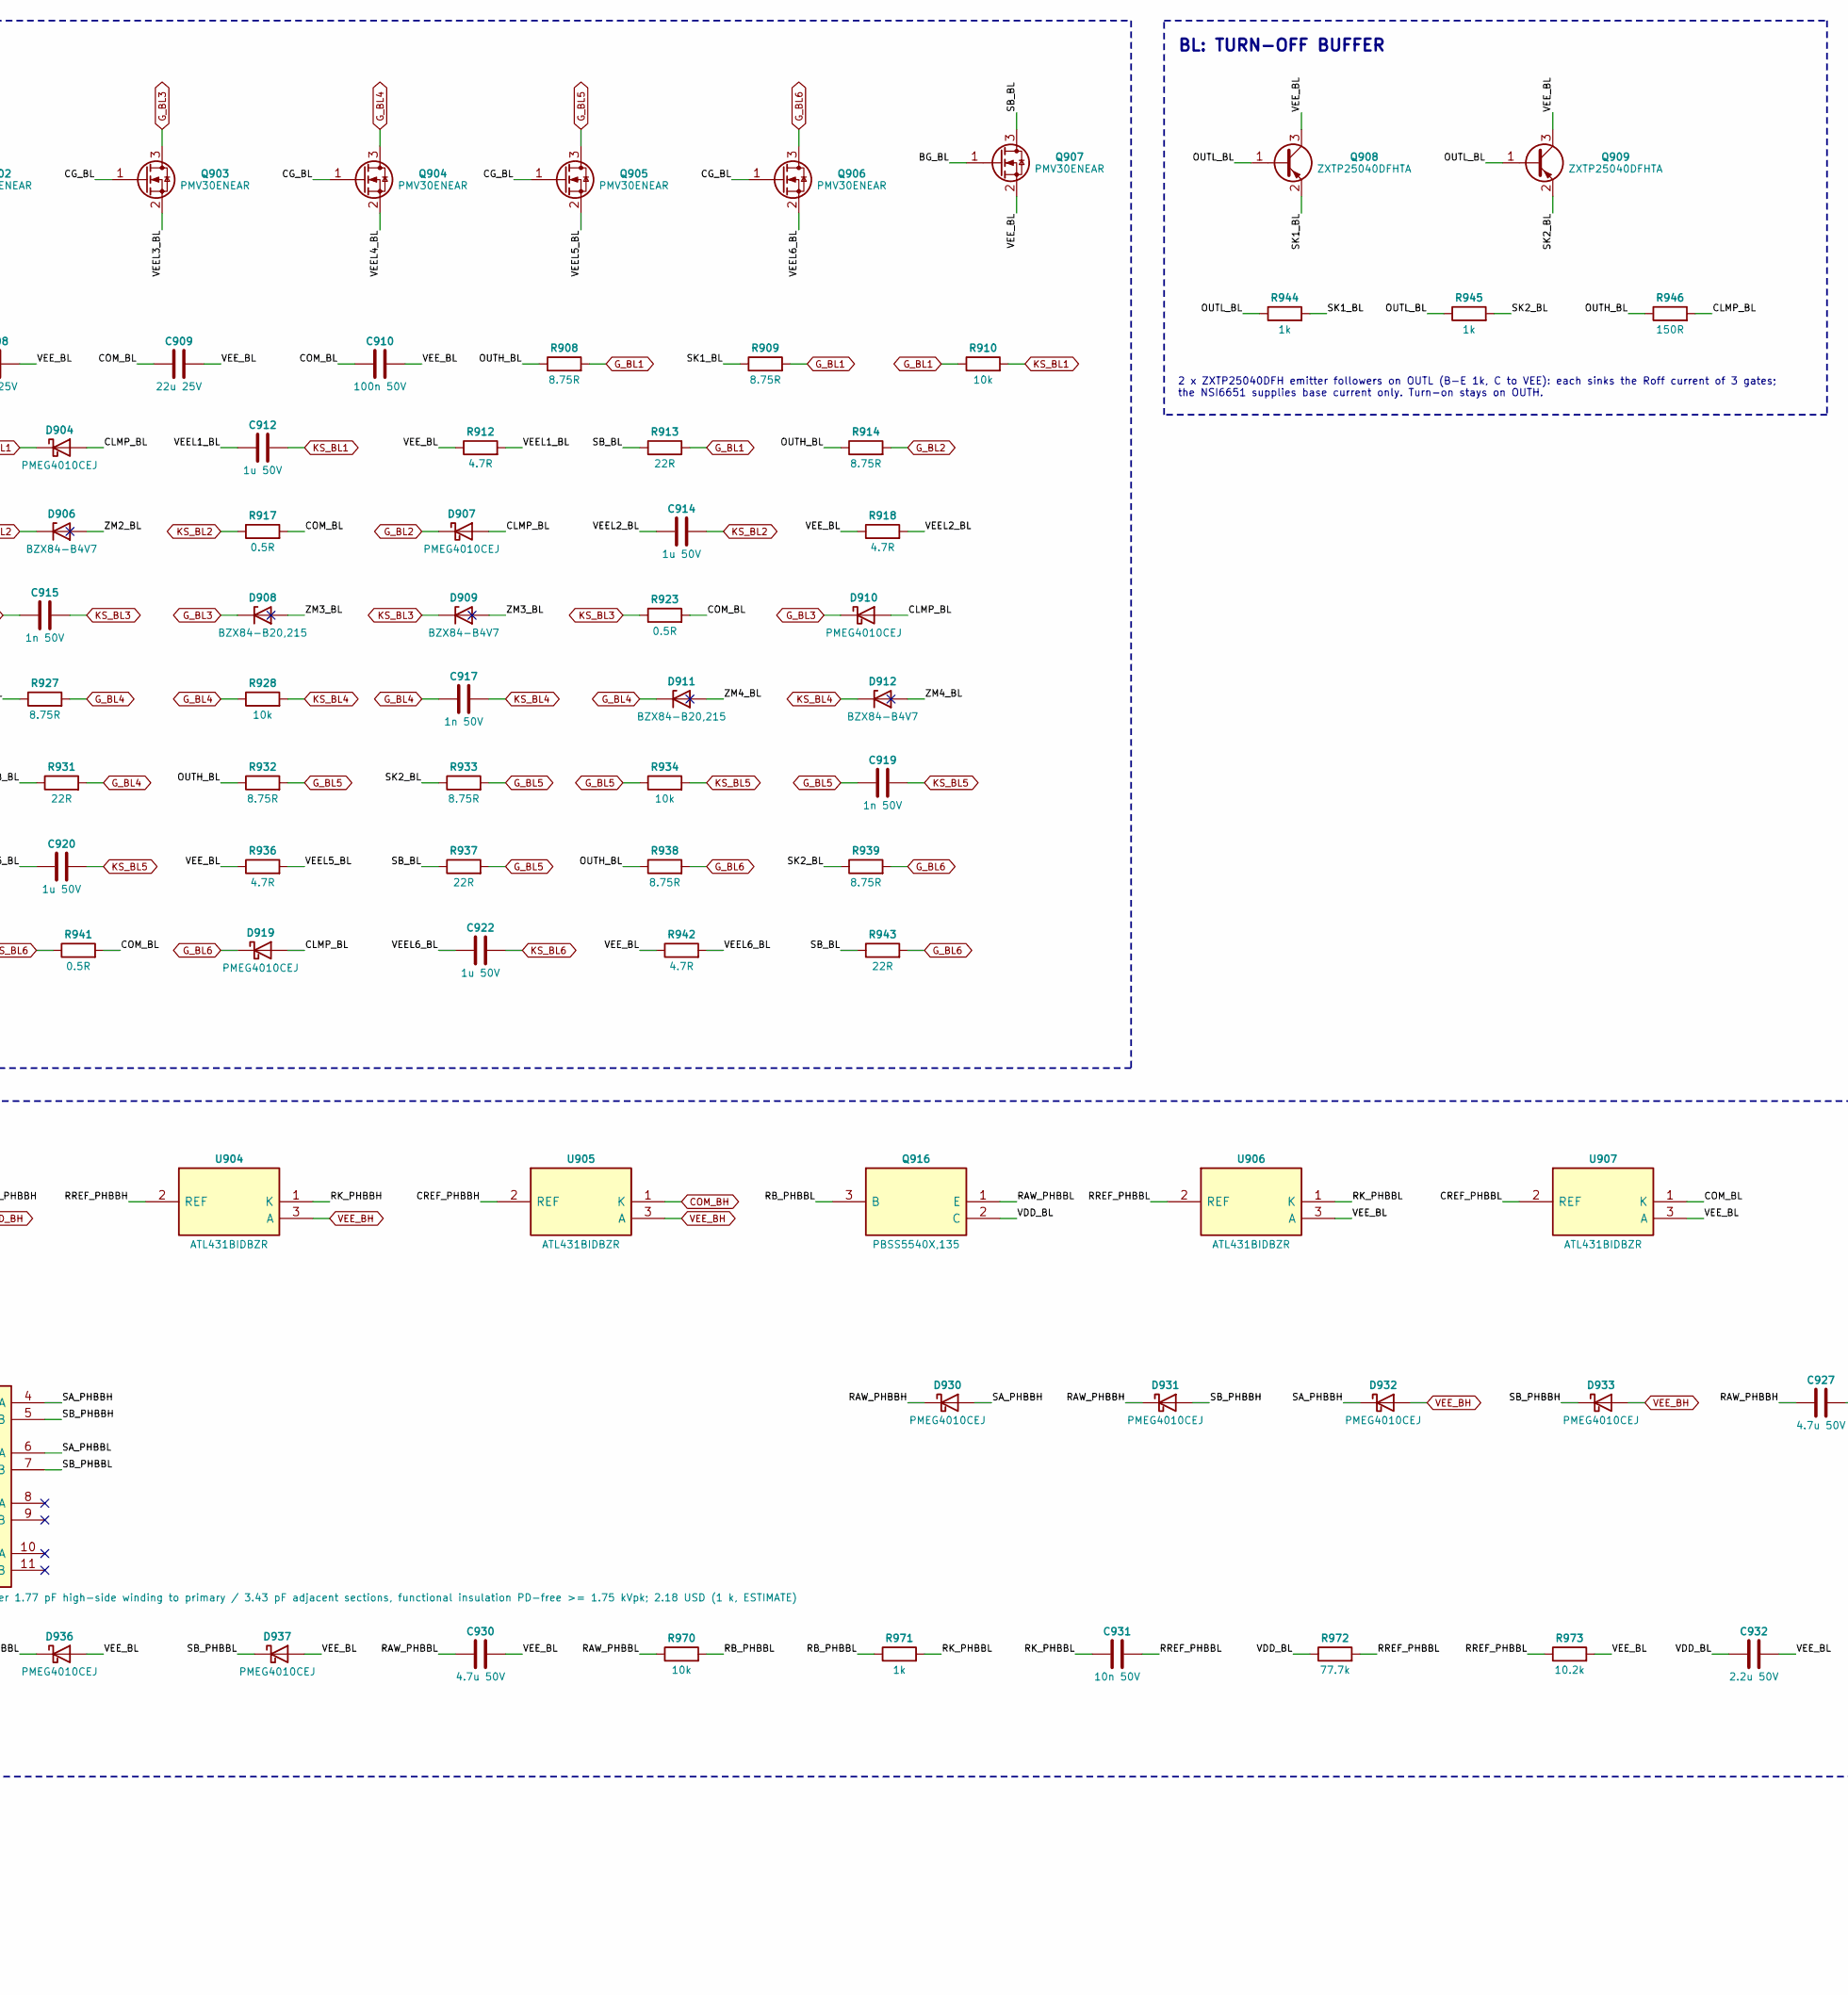
[picture p366: schematic 09_gdbl.kicad_sch, part in row 1, column 2]

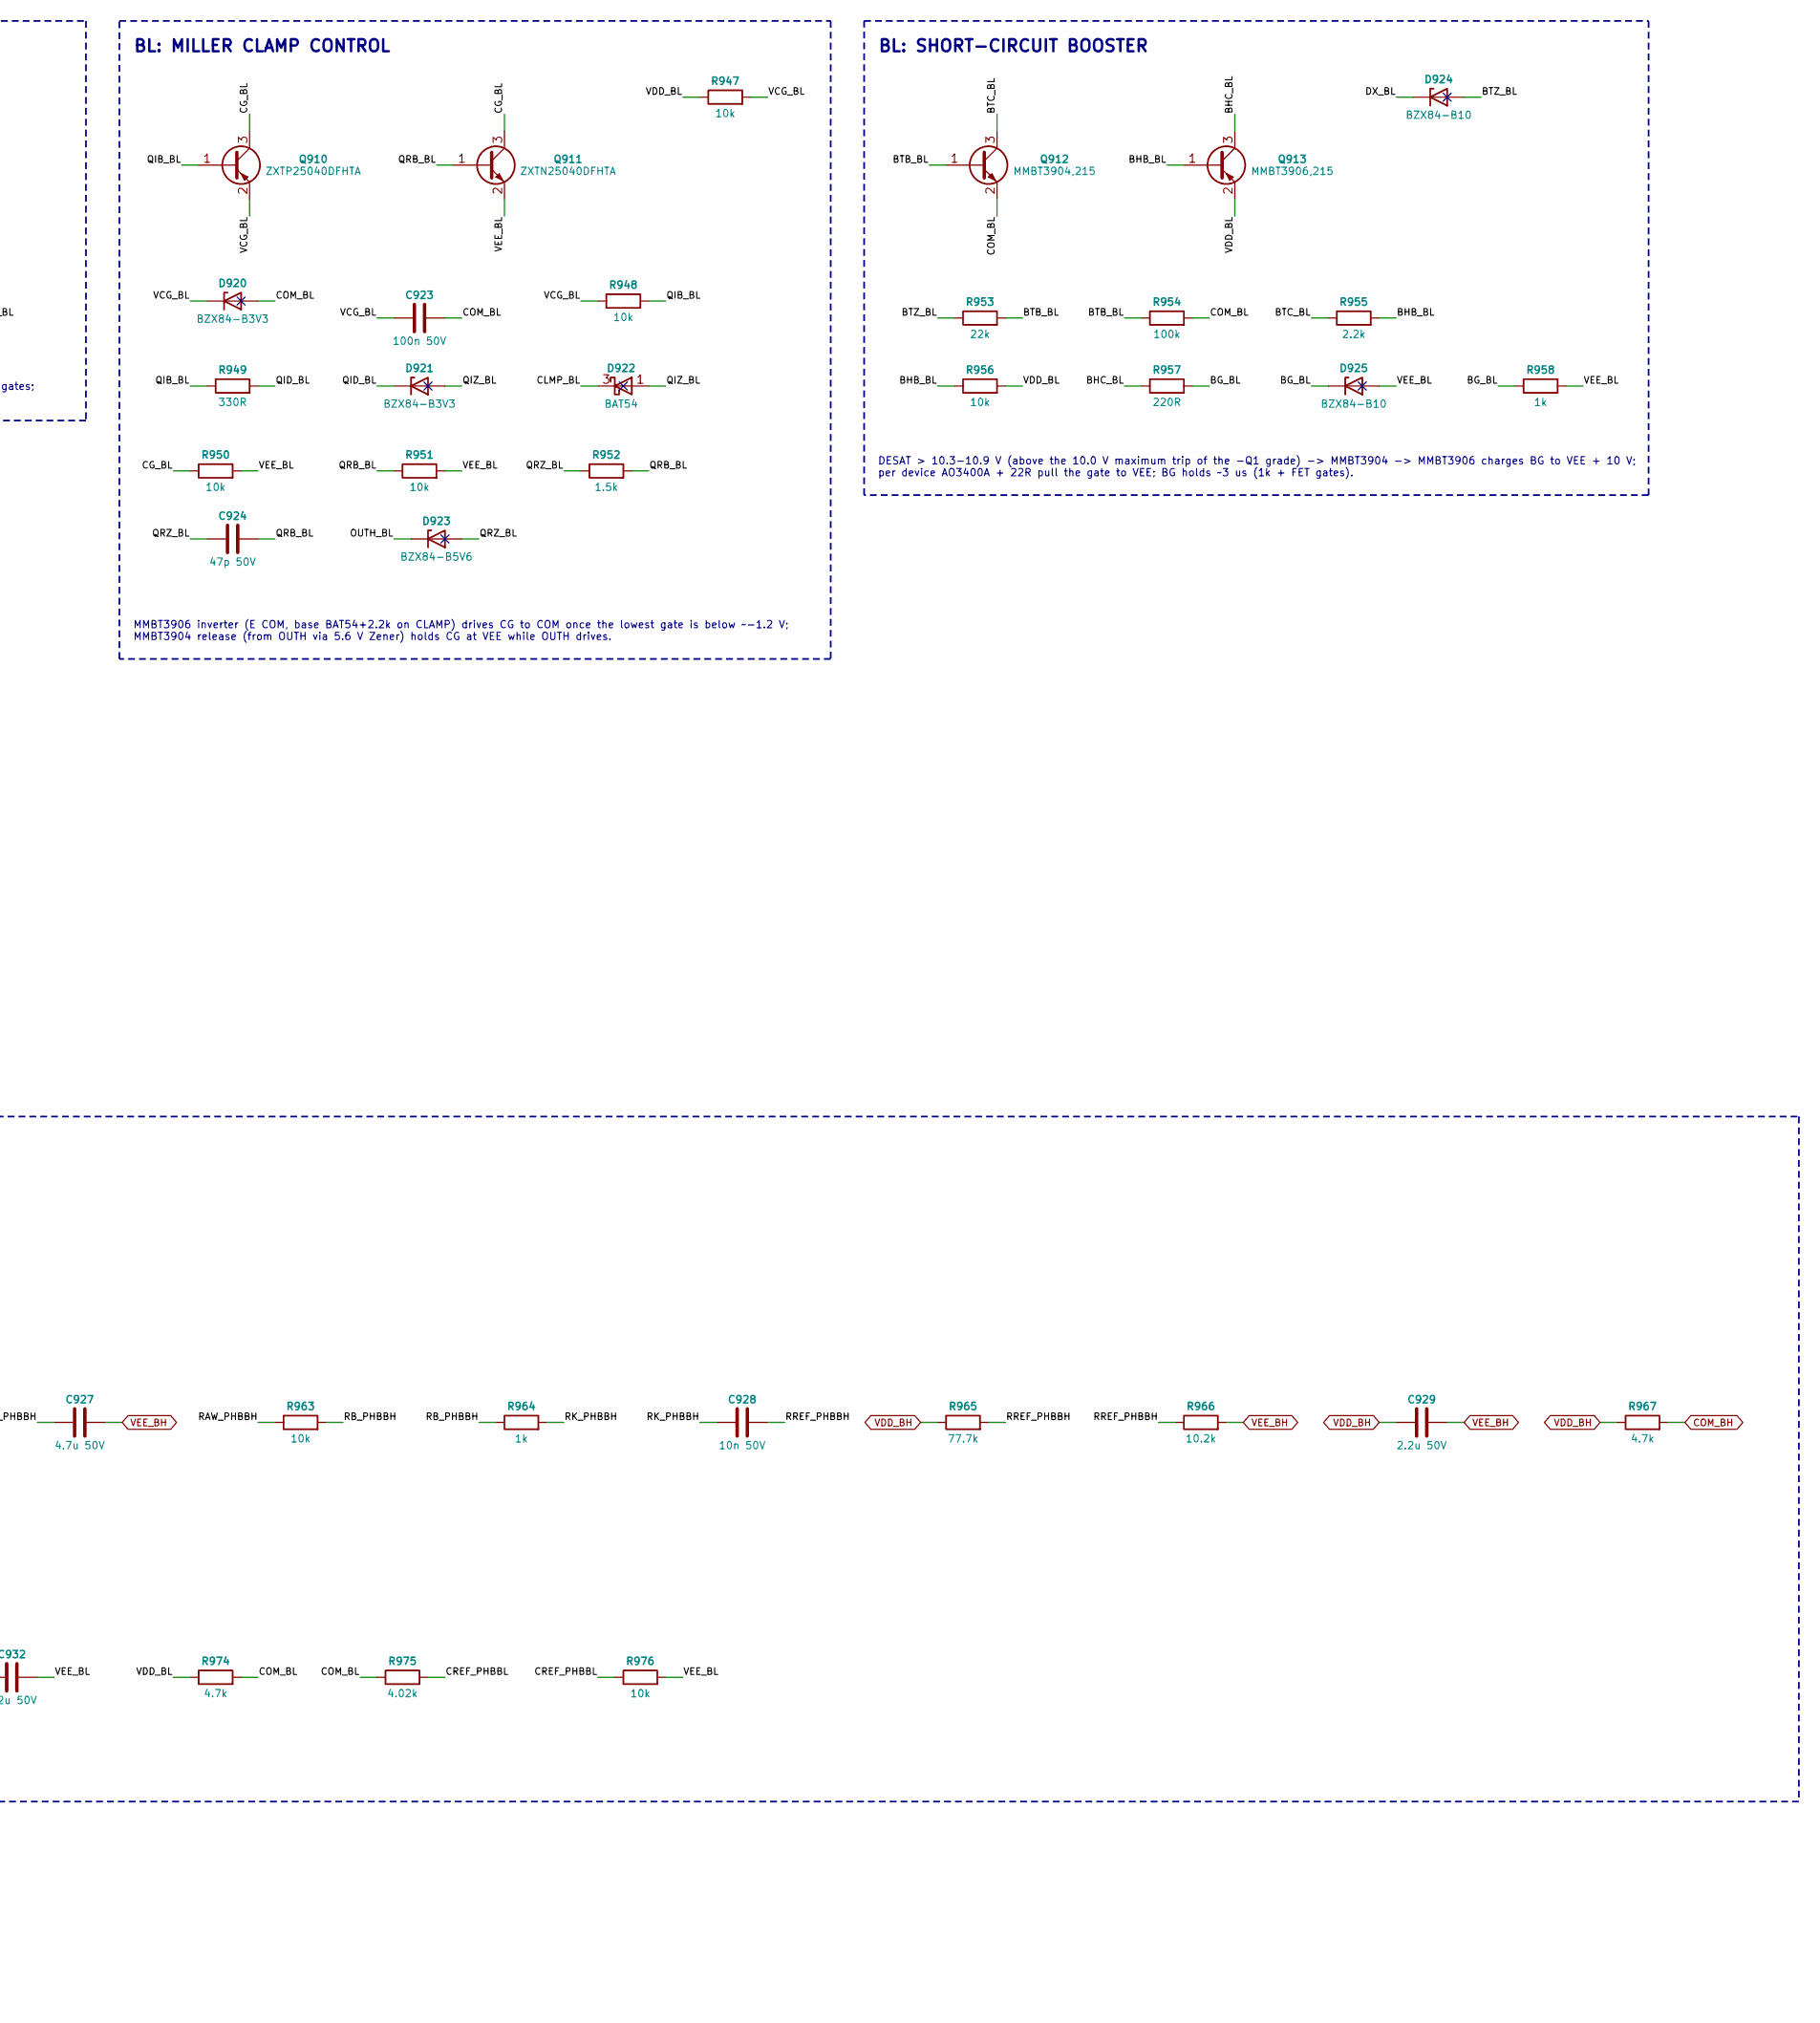
[picture p367: schematic 09_gdbl.kicad_sch, part in row 1, column 3]

Parts:
C901, C902, C904: 100p 50V
C903, C905, C907, C910, C923, C926: 100n 50V
C906: 10u 50V
C908, C909: 22u 25V
C911, C913, C915, C917, C919, C921: 1n 50V
C912, C914, C916, C918, C920, C922: 1u 50V
C924: 47p 50V
C925: 10u 16V
C927, C930: 4.7u 50V
C928, C931: 10n 50V
C929, C932: 2.2u 50V
D901, D922, D927: BAT54; MPN BAT54
D902, D905, D908, D911, D914, D917: BZX84-B20,215; MPN BZX84-B20,215
D903, D906, D909, D912, D915, D918: BZX84-B4V7; MPN BZX84-B4V7
D904, D907, D910, D913, D916, D919, D930, D931, D932, D933, D934, D935, D936, D937: PMEG4010CEJ; MPN PMEG4010CEJ
D920, D921: BZX84-B3V3; MPN BZX84-B3V3
D923: BZX84-B5V6; MPN BZX84-B5V6
D924, D925: BZX84-B10; MPN BZX84-B10
D926: BAT54S; MPN BAT54S
D928, D929: BYG23T-M3/TR; MPN BYG23T-M3/TR
Q901, Q902, Q903, Q904, Q905, Q906, Q907: PMV30ENEAR; MPN PMV30ENEAR
Q908, Q909, Q910: ZXTP25040DFHTA; MPN ZXTP25040DFHTA
Q911: ZXTN25040DFHTA; MPN ZXTN25040DFHTA
Q912, Q914: MMBT3904,215; MPN MMBT3904,215
Q913: MMBT3906,215; MPN MMBT3906,215
Q915, Q916: PBSS5540X,135; MPN PBSS5540X,135
R901, R910, R916, R922, R928, R934, R940, R947, R948, R950, R951, R956, R959, R962, R963, R969, R970, R976: 10k
R902, R904, R961: 100R
R903: 3.65k
R905: 0R
R906: 0R; not fitted
R907, R944, R945, R958, R964, R971: 1k
R908, R909, R914, R915, R920, R921, R926, R927, R932, R933, R938, R939: 8.75R
R911, R917, R923, R929, R935, R941: 0.5R
R912, R918, R924, R930, R936, R942: 4.7R
R913, R919, R925, R931, R937, R943: 22R
R946: 150R
R949: 330R
R952: 1.5k
R953: 22k
R954, R960: 100k
R955: 2.2k
R957: 220R
R965, R972: 77.7k
R966, R973: 10.2k
R967, R974: 4.7k
R968, R975: 4.02k
T901: Gate-bias transformer per phase (sim/out/magnetic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
U901: SN74LVC1G17DBVR; MPN SN74LVC1G17DBVR
U902: NSI6651ASC-Q1SWR; MPN NSI6651ASC-Q1SWR
U903: SN6505BDBVR; MPN SN6505BDBVR
U904, U905, U906, U907: ATL431BIDBZR; MPN ATL431BIDBZR

Connections:
+5V: C903.1, C905.1, U901.5 (VCC), U902.15 (VCC1)
+5V_GD: C925.1, C926.1, T901.2 (CT), U903.2 (VCC)
BG_BL: D925.3 (K), Q907.1 (G), R957.2, R958.1
BHB_BL: Q913.1 (B), R955.2, R956.1
BHC_BL: Q913.3 (C), R957.1
BIAS_EN5G: R962.1, U903.5 (EN)
BTB_BL: Q912.1 (B), R953.2, R954.1
BTC_BL: Q912.3 (C), R955.1
BTZ_BL: D924.1 (A), R953.1
CG_BL: Q901.1 (G), Q902.1 (G), Q903.1 (G), Q904.1 (G), Q905.1 (G), Q906.1 (G), Q910.3 (C), Q911.3 (C), R950.1
CLMP_BL: D904.2 (A), D907.2 (A), D910.2 (A), D913.2 (A), D916.2 (A), D919.2 (A), D922.3 (K), R946.2, U902.7 (CLAMP)
COM_BH: R967.2, R968.1, U905.1 (K)
COM_BL: C906.2, C907.2, C908.1, C909.1, C910.1, C923.2, D920.1 (A), D926.1 (A), Q912.2 (E), R906.2, R911.2, R917.2, R923.2, R929.2, R935.2, R941.2, R954.2, R959.1, R974.2, R975.1, U902.3 (GND2), U907.1 (K)
CREF_PHBBH: R968.2, R969.1, U905.2 (REF)
CREF_PHBBL: R975.2, R976.1, U907.2 (REF)
D1_PHB: T901.1 (D1), U903.1 (D1)
D2_PHB: T901.3 (D2), U903.3 (D2)
DS1_BL: D928.1 (K), D929.2 (A)
DTB_BL: R904.1, U901.4 (Y)
DTS_BL: C902.1, D901.3 (K), R903.2, U901.2 (A)
DX_BL: D924.3 (K), D926.3 (COM), D927.3 (K), R961.1, U902.2 (DESAT)
DY_BL: D928.2 (A), R961.2
EN5: U902.14 (~RST/EN)
FLT_N: U902.13 (~FLT)
GND: C901.2, C902.2, C903.2, C904.2, C905.2, C925.2, C926.2, R901.2, R907.2, R962.2, U901.3 (GND), U902.9 (GND1), U903.4 (GND), U903.6 (CLK)
G_BL1: C911.1, D902.3 (K), D904.1 (K), Q901.3 (D), R908.2, R909.2, R910.1, R913.2
G_BL2: C913.1, D905.3 (K), D907.1 (K), Q902.3 (D), R914.2, R915.2, R916.1, R919.2
G_BL3: C915.1, D908.3 (K), D910.1 (K), Q903.3 (D), R920.2, R921.2, R922.1, R925.2
G_BL4: C917.1, D911.3 (K), D913.1 (K), Q904.3 (D), R926.2, R927.2, R928.1, R931.2
G_BL5: C919.1, D914.3 (K), D916.1 (K), Q905.3 (D), R932.2, R933.2, R934.1, R937.2
G_BL6: C921.1, D917.3 (K), D919.1 (K), Q906.3 (D), R938.2, R939.2, R940.1, R943.2
INN_BL: C904.1, R904.2, U902.11 (IN-)
INP_BL: C901.1, R902.2, U902.10 (IN+)
KS_BL1: C911.2, C912.2, D903.3 (K), R910.2, R911.1
KS_BL2: C913.2, C914.2, D906.3 (K), R916.2, R917.1
KS_BL3: C915.2, C916.2, D909.3 (K), R922.2, R923.1
KS_BL4: C917.2, C918.2, D912.3 (K), R928.2, R929.1
KS_BL5: C919.2, C920.2, D915.3 (K), R934.2, R935.1
KS_BL6: C921.2, C922.2, D918.3 (K), R940.2, R941.1
NDB_BL: Q914.1 (B), R959.2
NDX_BL: D927.1 (A), Q914.3 (C), R960.2
OUTH_BL: D923.3 (K), R908.1, R914.1, R920.1, R926.1, R932.1, R938.1, R946.1, U902.4 (OUTH)
OUTL_BL: Q908.1 (B), Q909.1 (B), R944.1, R945.1, U902.6 (OUTL)
P1_BL: R905.1, R906.1, U902.1 (VEE2)
P16_BL: R907.1, U902.16 (TEST)
PWM3_5V: D901.1 (A), R903.1
PWM4_5V: R901.1, R902.1
QIB_BL: Q910.1 (B), R948.2, R949.1
QID_BL: D921.3 (K), R949.2
QIZ_BL: D921.1 (A), D922.1 (A)
QRB_BL: C924.2, Q911.1 (B), R951.1, R952.2
QRZ_BL: C924.1, D923.1 (A), R952.1
RAW_PHBBH: C927.1, D930.1 (K), D931.1 (K), Q915.1 (E), R963.1
RAW_PHBBL: C930.1, D934.1 (K), D935.1 (K), Q916.1 (E), R970.1
RB_PHBBH: Q915.3 (B), R963.2, R964.1
RB_PHBBL: Q916.3 (B), R970.2, R971.1
RDY: U902.12 (RDY)
RK_PHBBH: C928.1, R964.2, U904.1 (K)
RK_PHBBL: C931.1, R971.2, U906.1 (K)
RREF_PHBBH: C928.2, R965.2, R966.1, U904.2 (REF)
RREF_PHBBL: C931.2, R972.2, R973.1, U906.2 (REF)
SA_PHBBH: D930.2 (A), D932.1 (K), T901.4 (S1A)
SA_PHBBL: D934.2 (A), D936.1 (K), T901.6 (S2A)
SB_BL: Q907.3 (D), R913.1, R919.1, R925.1, R931.1, R937.1, R943.1
SB_PHBBH: D931.2 (A), D933.1 (K), T901.5 (S1B)
SB_PHBBL: D935.2 (A), D937.1 (K), T901.7 (S2B)
SK1_BL: Q908.2 (E), R909.1, R915.1, R921.1, R944.2
SK2_BL: Q909.2 (E), R927.1, R933.1, R939.1, R945.2
SW_B: D929.1 (K)
VCG_BL: C923.1, D920.3 (K), Q910.2 (E), R947.2, R948.1
VDD_BH: C929.1, Q915.2 (C), R965.1, R967.1
VDD_BL: C906.1, C907.1, C932.1, D926.2 (K), Q913.2 (E), Q916.2 (C), R947.1, R956.2, R960.1, R972.1, R974.1, U902.5 (VCC2)
VEEL1_BL: C912.1, Q901.2 (S), R912.2
VEEL2_BL: C914.1, Q902.2 (S), R918.2
VEEL3_BL: C916.1, Q903.2 (S), R924.2
VEEL4_BL: C918.1, Q904.2 (S), R930.2
VEEL5_BL: C920.1, Q905.2 (S), R936.2
VEEL6_BL: C922.1, Q906.2 (S), R942.2
VEE_BH: C927.2, C929.2, D932.2 (A), D933.2 (A), R966.2, R969.2, U904.3 (A), U905.3 (A)
VEE_BL: C908.2, C909.2, C910.2, C930.2, C932.2, D925.1 (A), D936.2 (A), D937.2 (A), Q907.2 (S), Q908.3 (C), Q909.3 (C), Q911.2 (E), Q914.2 (E), R905.2, R912.1, R918.1, R924.1, R930.1, R936.1, R942.1, R950.2, R951.2, R958.2, R973.2, R976.2, U902.8 (VEE2), U906.3 (A), U907.3 (A)
ZM1_BL: D902.1 (A), D903.1 (A)
ZM2_BL: D905.1 (A), D906.1 (A)
ZM3_BL: D908.1 (A), D909.1 (A)
ZM4_BL: D911.1 (A), D912.1 (A)
ZM5_BL: D914.1 (A), D915.1 (A)
ZM6_BL: D917.1 (A), D918.1 (A)

Notes on the sheet:
BL: DESAT
Per device: Ron/Roff, 0.5R Kelvin R to the COM star, 10k and Zeners (about +21 V / -5.7 V) on its own Kelvin net. Miller hold: N-MOSFET clamp (PMV30ENEA) gate-pin to a local VEE (1u on the Kelvin pin). LAYOUT: FET + 1u at the device, loop <= 1 nH.
BL: LOGIC SIDE
IN+ = own PWM; IN- = complementary switch, falling edge stretched 3.65k/100p (interlock + min dead time = max(firmware, hardware)). Bias PG (active low) pulls RDY low.
DESAT pin (internal 500 uA blanking source, trip 8.5-10.0 V) - Rs - 2 x BYG23T-M3/TR (1300 V each) - drain. BAT54S keeps DX between COM and VDD against dv/dt through the string; Cblk footprint DNP.
BL: SHORT-CIRCUIT BOOSTER
2 x ZXTP25040DFH emitter followers on OUTL (B-E 1k, C to VEE): each sinks the Roff current of 3 gates; the NSI6651 supplies base current only. Turn-on stays on OUTH.
BL: DRIVER AND 6 GATES
PHB: GATE BIAS (PER PHASE)
LEG B: LAYOUT RULES
BL: TURN-OFF BUFFER
MMBT3906 inverter (E COM, base BAT54+2.2k on CLAMP) drives CG to COM once the lowest gate is below ~-1.2 V; MMBT3904 release (from OUTH via 5.6 V Zener) holds CG at VEE while OUTH drives.
SN6505B push-pull 420 kHz from +5V_GD, BIAS_EN high = on; T_BIAS4 custom, functional insulation (PD-free >= 1.75 kVpk, <= 5 pF per secondary). Per channel: bridge, PNP regulator VDD-VEE, ATL431 COM split.
Gate and Kelvin of each device as coupled pairs of equal length from the COM star; Ron, Roff, Kelvin R, 10k + 1n, Zeners and the clamp FET + C_VL at each device (loop <= 1 nH). PNP followers next to their three gates. DESAT string >= 2.5 mm pad gap per diode; coat to PD1. Miller hold of six gates N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
BL: MILLER CLAMP CONTROL
DESAT > 10.3-10.9 V (above the 10.0 V maximum trip of the -Q1 grade) -> MMBT3904 -> MMBT3906 charges BG to VEE + 10 V; per device AO3400A + 22R pull the gate to VEE; BG holds ~3 us (1k + FET gates).
