vectivolt/PCM/hardware/PCS-PWR/sheets/11_gdcl.kicad_sch

## KiCad design hardware/PCS-PWR/sheets/11_gdcl.kicad_sch (2026-10-07)

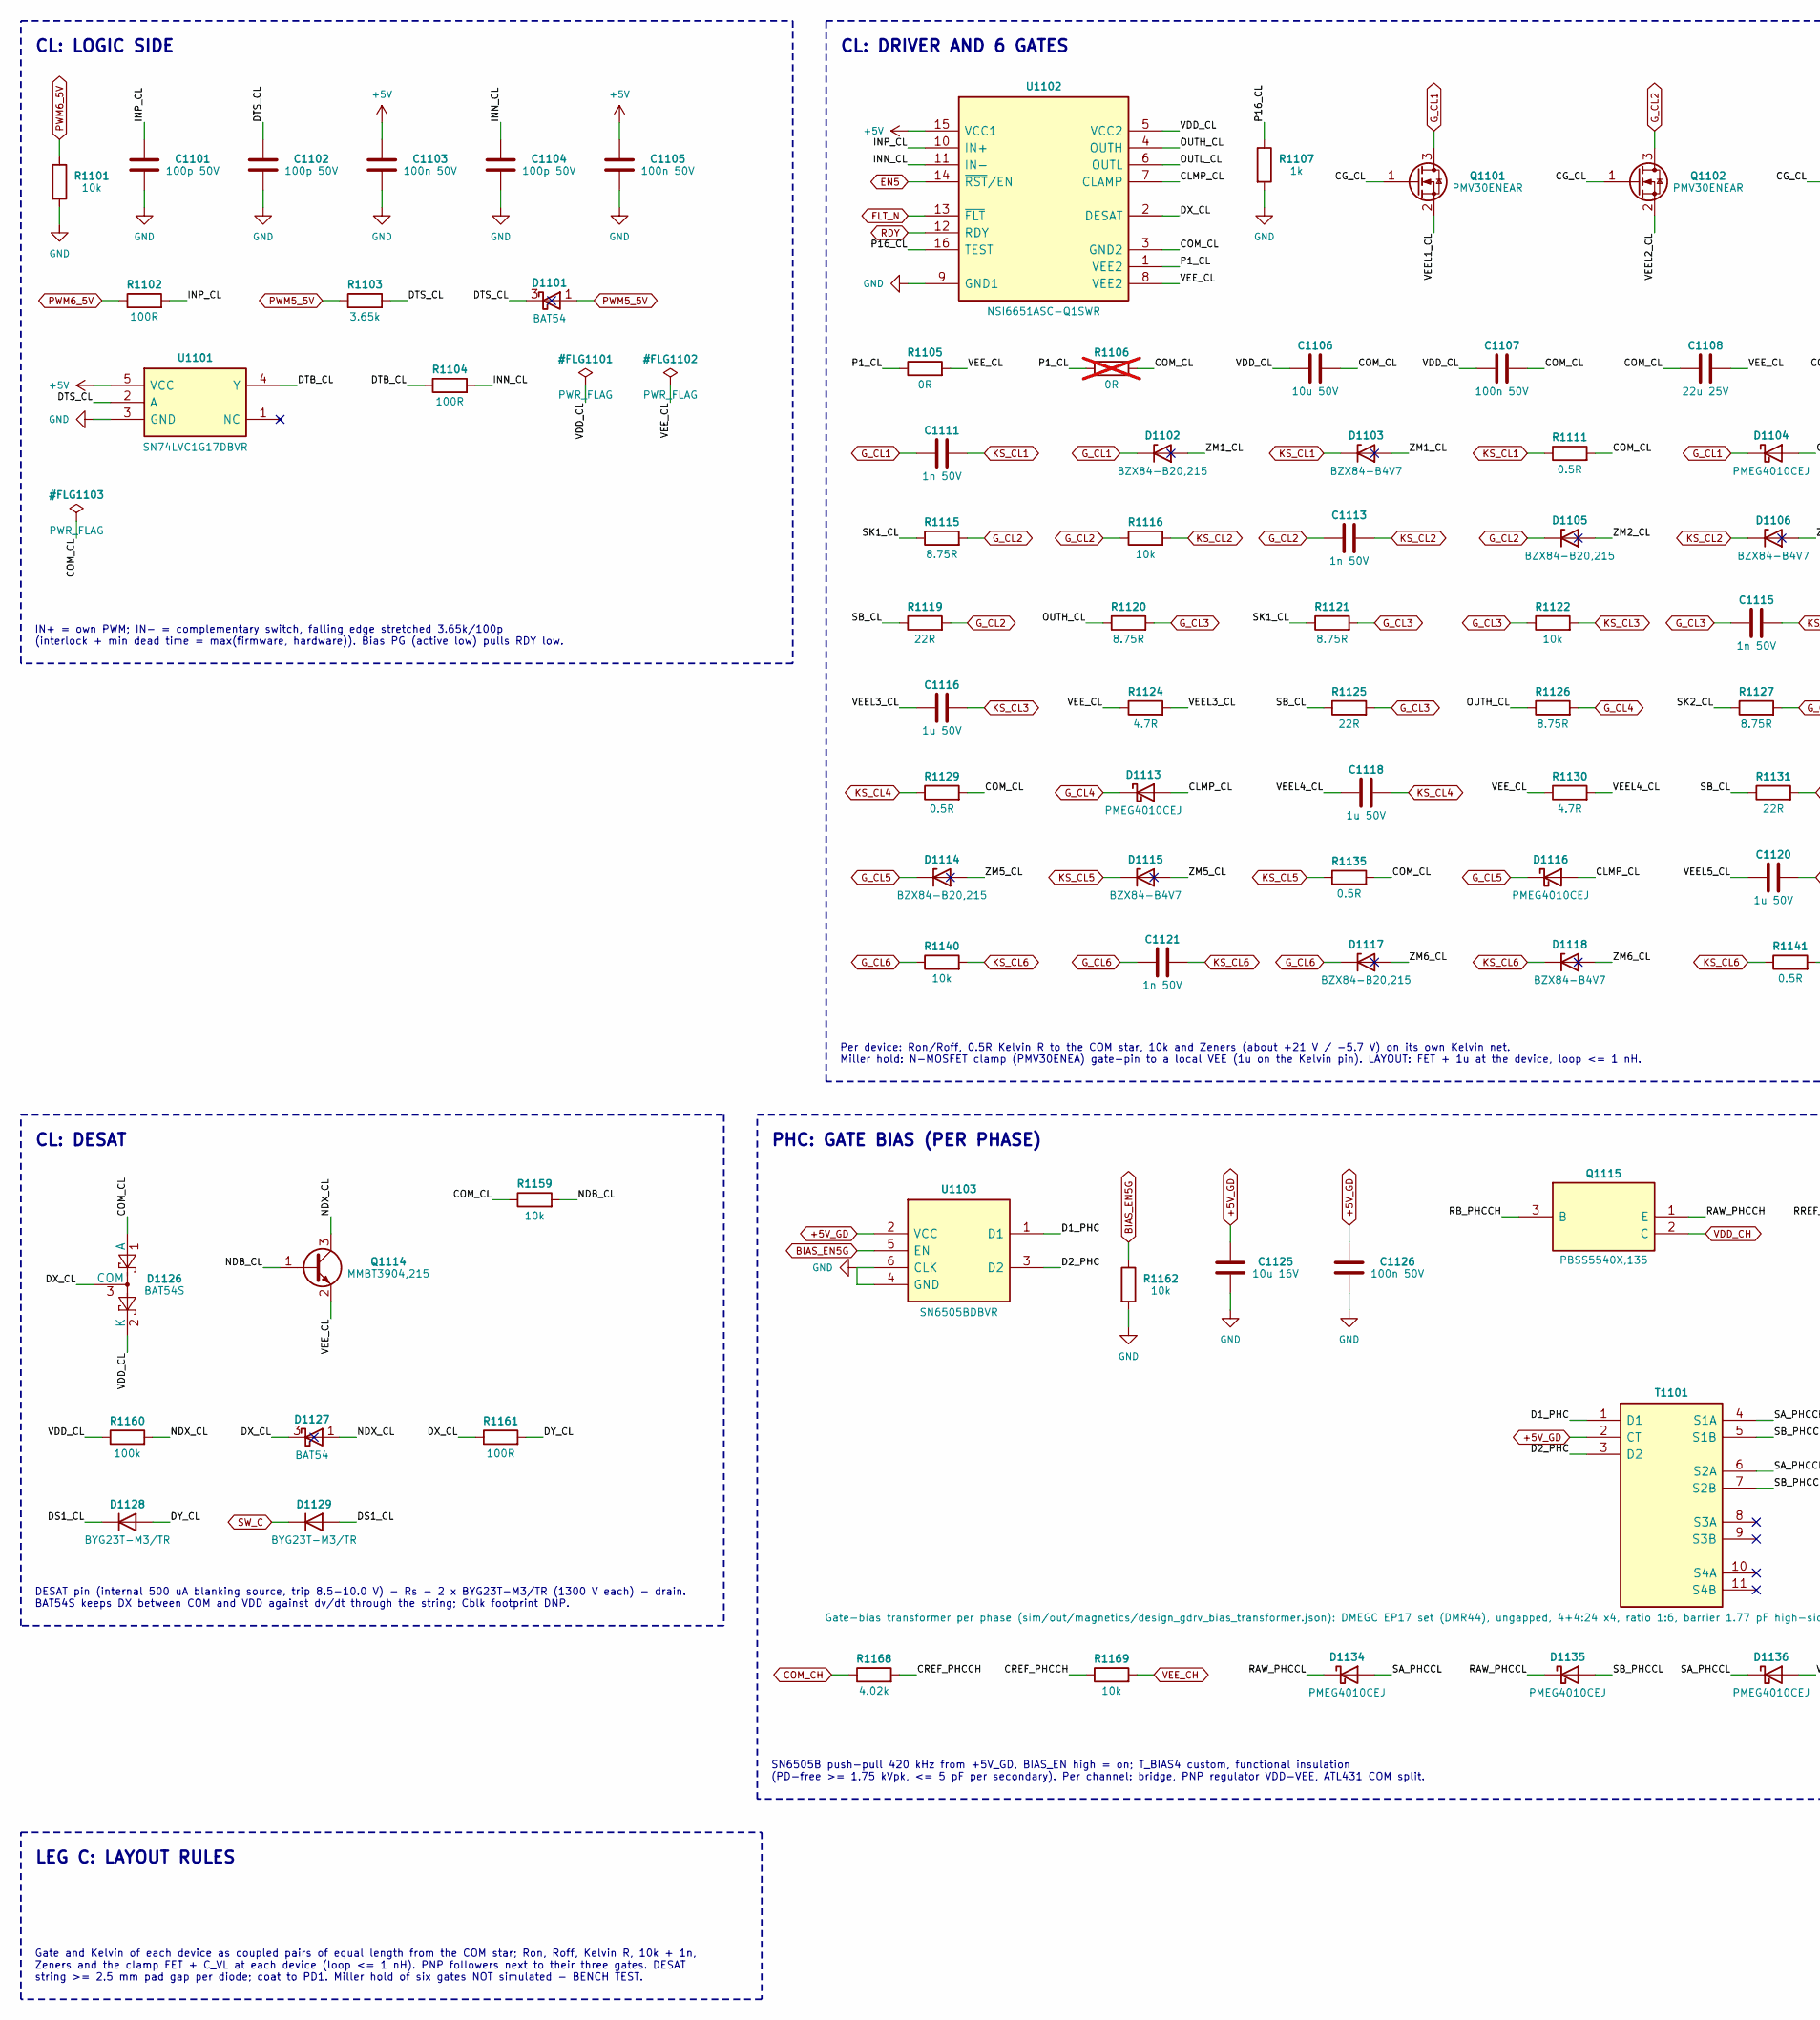
[picture p370: schematic 11_gdcl.kicad_sch, part in row 1, column 1]

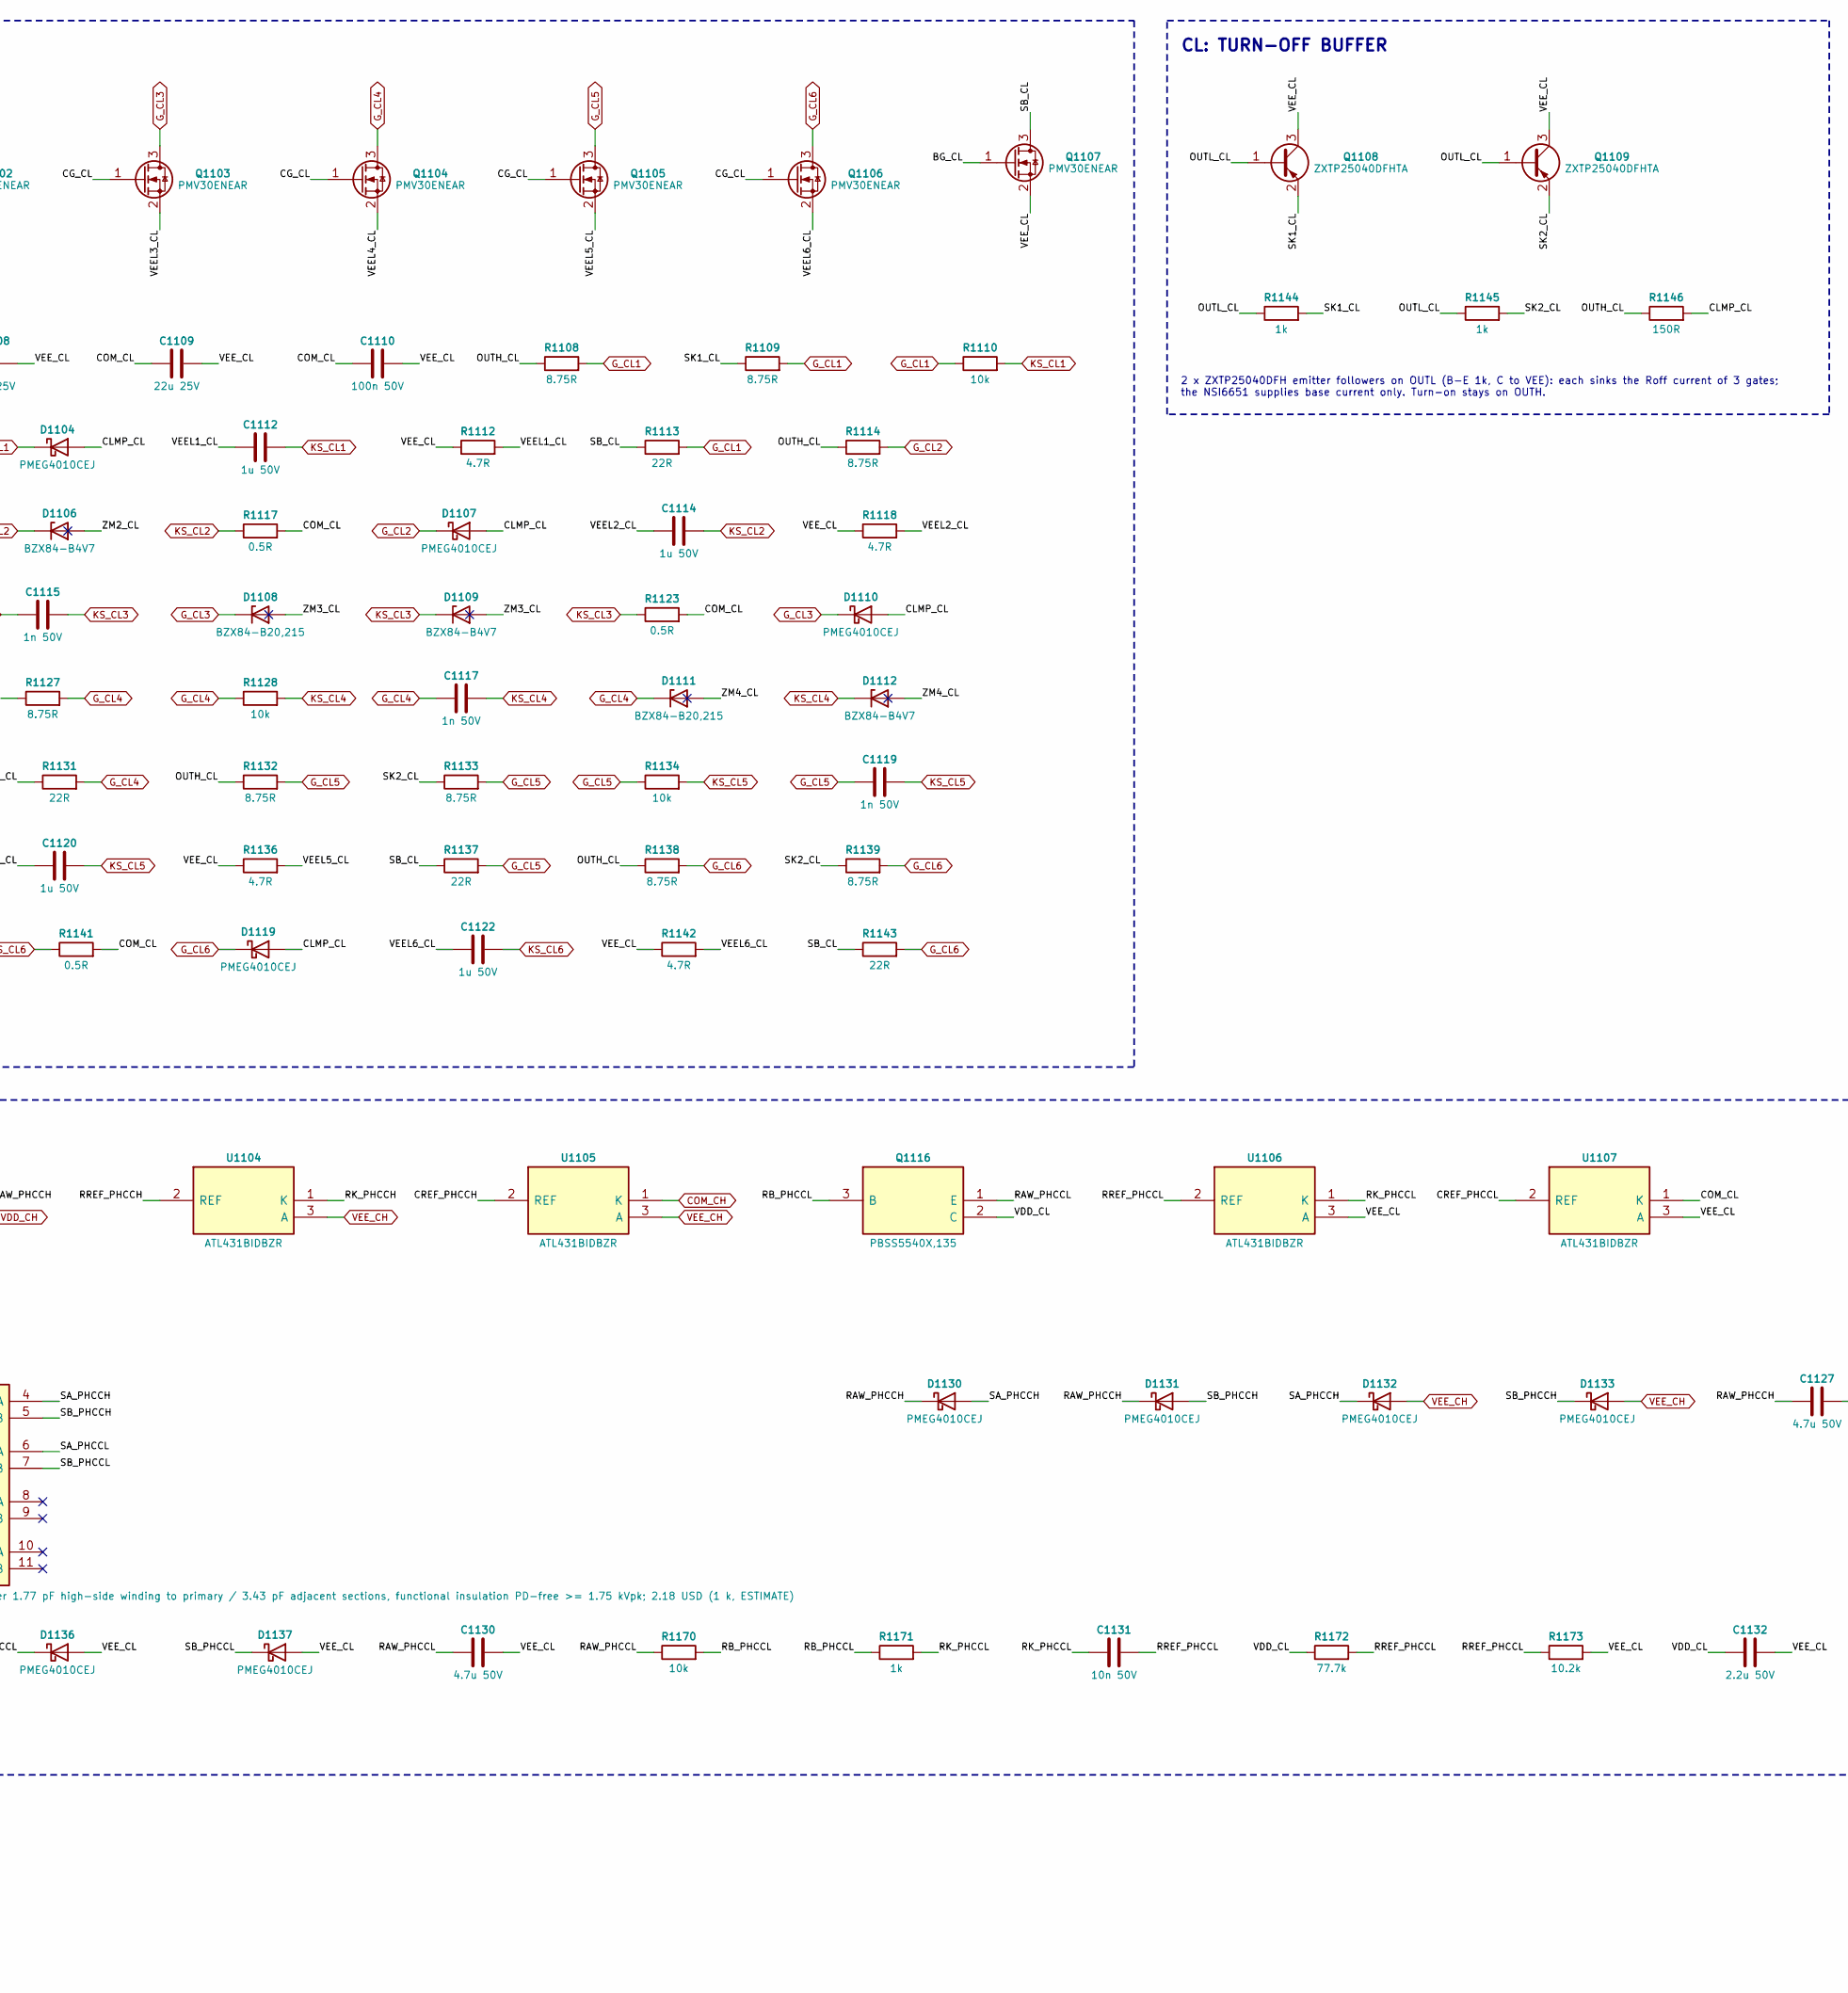
[picture p371: schematic 11_gdcl.kicad_sch, part in row 1, column 2]

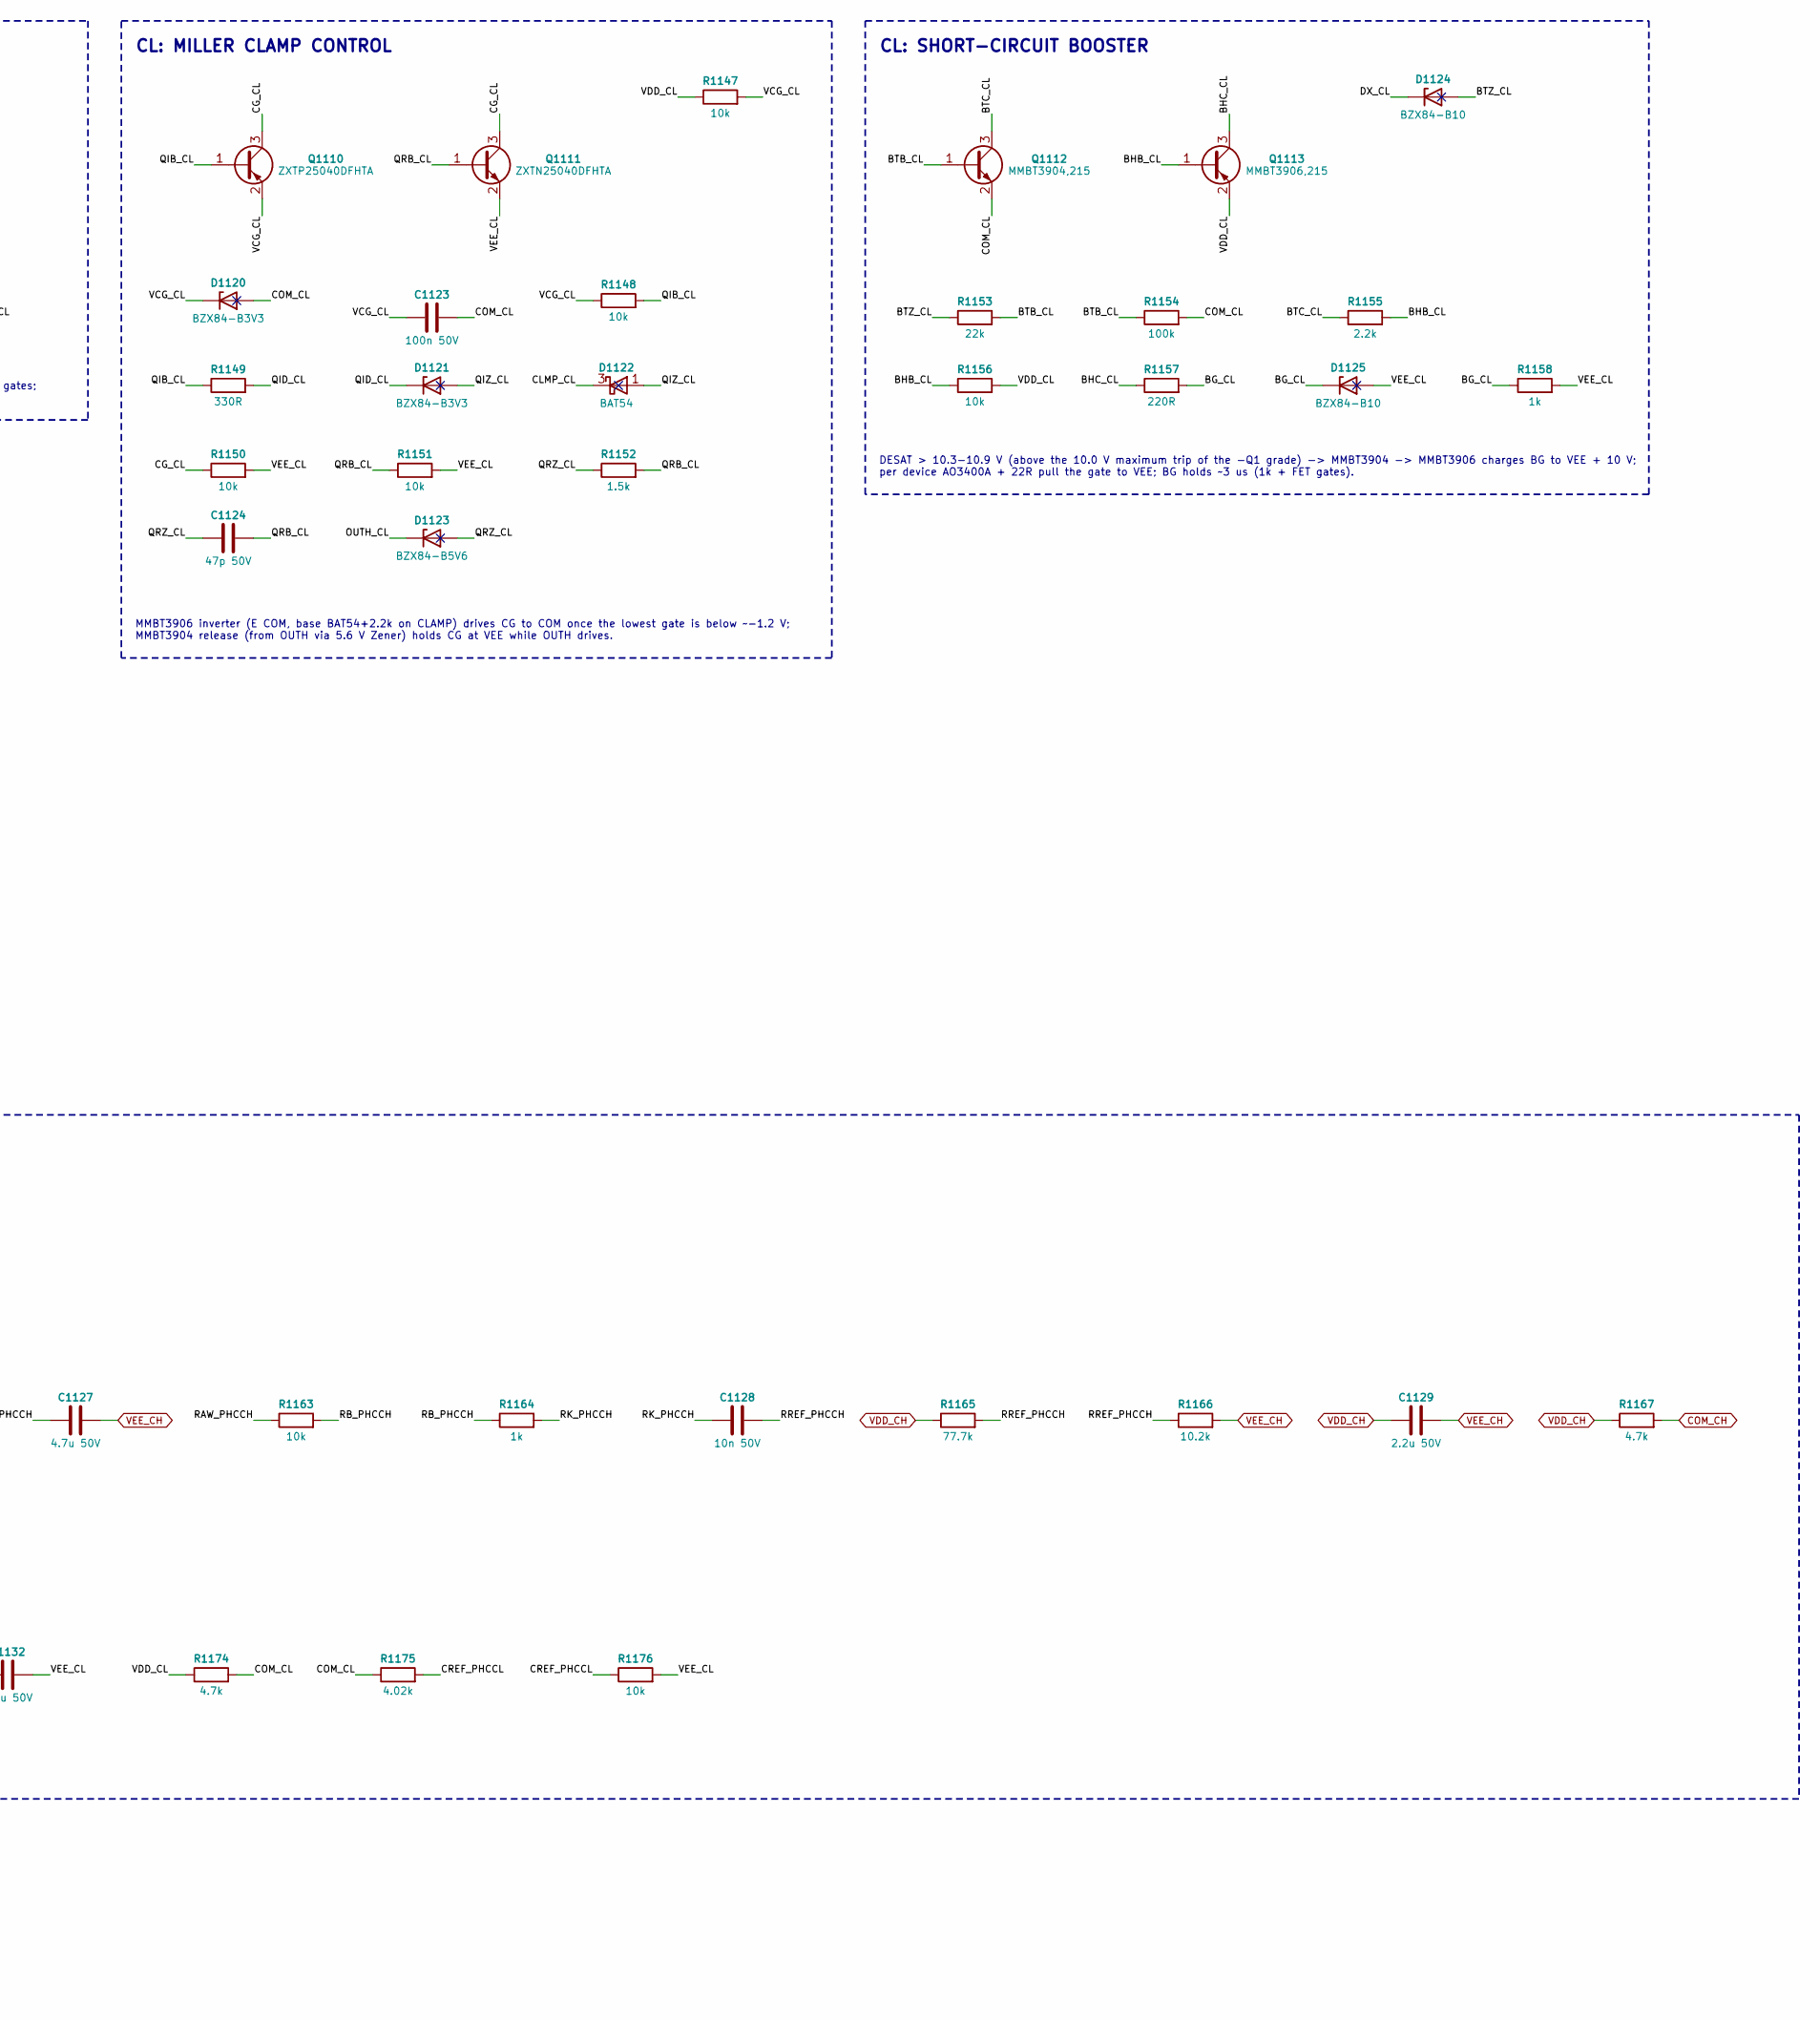
[picture p372: schematic 11_gdcl.kicad_sch, part in row 1, column 3]

Parts:
C1101, C1102, C1104: 100p 50V
C1103, C1105, C1107, C1110, C1123, C1126: 100n 50V
C1106: 10u 50V
C1108, C1109: 22u 25V
C1111, C1113, C1115, C1117, C1119, C1121: 1n 50V
C1112, C1114, C1116, C1118, C1120, C1122: 1u 50V
C1124: 47p 50V
C1125: 10u 16V
C1127, C1130: 4.7u 50V
C1128, C1131: 10n 50V
C1129, C1132: 2.2u 50V
D1101, D1122, D1127: BAT54; MPN BAT54
D1102, D1105, D1108, D1111, D1114, D1117: BZX84-B20,215; MPN BZX84-B20,215
D1103, D1106, D1109, D1112, D1115, D1118: BZX84-B4V7; MPN BZX84-B4V7
D1104, D1107, D1110, D1113, D1116, D1119, D1130, D1131, D1132, D1133, D1134, D1135, D1136, D1137: PMEG4010CEJ; MPN PMEG4010CEJ
D1120, D1121: BZX84-B3V3; MPN BZX84-B3V3
D1123: BZX84-B5V6; MPN BZX84-B5V6
D1124, D1125: BZX84-B10; MPN BZX84-B10
D1126: BAT54S; MPN BAT54S
D1128, D1129: BYG23T-M3/TR; MPN BYG23T-M3/TR
Q1101, Q1102, Q1103, Q1104, Q1105, Q1106, Q1107: PMV30ENEAR; MPN PMV30ENEAR
Q1108, Q1109, Q1110: ZXTP25040DFHTA; MPN ZXTP25040DFHTA
Q1111: ZXTN25040DFHTA; MPN ZXTN25040DFHTA
Q1112, Q1114: MMBT3904,215; MPN MMBT3904,215
Q1113: MMBT3906,215; MPN MMBT3906,215
Q1115, Q1116: PBSS5540X,135; MPN PBSS5540X,135
R1101, R1110, R1116, R1122, R1128, R1134, R1140, R1147, R1148, R1150, R1151, R1156, R1159, R1162, R1163, R1169, R1170, R1176: 10k
R1102, R1104, R1161: 100R
R1103: 3.65k
R1105: 0R
R1106: 0R; not fitted
R1107, R1144, R1145, R1158, R1164, R1171: 1k
R1108, R1109, R1114, R1115, R1120, R1121, R1126, R1127, R1132, R1133, R1138, R1139: 8.75R
R1111, R1117, R1123, R1129, R1135, R1141: 0.5R
R1112, R1118, R1124, R1130, R1136, R1142: 4.7R
R1113, R1119, R1125, R1131, R1137, R1143: 22R
R1146: 150R
R1149: 330R
R1152: 1.5k
R1153: 22k
R1154, R1160: 100k
R1155: 2.2k
R1157: 220R
R1165, R1172: 77.7k
R1166, R1173: 10.2k
R1167, R1174: 4.7k
R1168, R1175: 4.02k
T1101: Gate-bias transformer per phase (sim/out/magnetic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
U1101: SN74LVC1G17DBVR; MPN SN74LVC1G17DBVR
U1102: NSI6651ASC-Q1SWR; MPN NSI6651ASC-Q1SWR
U1103: SN6505BDBVR; MPN SN6505BDBVR
U1104, U1105, U1106, U1107: ATL431BIDBZR; MPN ATL431BIDBZR

Connections:
+5V: C1103.1, C1105.1, U1101.5 (VCC), U1102.15 (VCC1)
+5V_GD: C1125.1, C1126.1, T1101.2 (CT), U1103.2 (VCC)
BG_CL: D1125.3 (K), Q1107.1 (G), R1157.2, R1158.1
BHB_CL: Q1113.1 (B), R1155.2, R1156.1
BHC_CL: Q1113.3 (C), R1157.1
BIAS_EN5G: R1162.1, U1103.5 (EN)
BTB_CL: Q1112.1 (B), R1153.2, R1154.1
BTC_CL: Q1112.3 (C), R1155.1
BTZ_CL: D1124.1 (A), R1153.1
CG_CL: Q1101.1 (G), Q1102.1 (G), Q1103.1 (G), Q1104.1 (G), Q1105.1 (G), Q1106.1 (G), Q1110.3 (C), Q1111.3 (C), R1150.1
CLMP_CL: D1104.2 (A), D1107.2 (A), D1110.2 (A), D1113.2 (A), D1116.2 (A), D1119.2 (A), D1122.3 (K), R1146.2, U1102.7 (CLAMP)
COM_CH: R1167.2, R1168.1, U1105.1 (K)
COM_CL: C1106.2, C1107.2, C1108.1, C1109.1, C1110.1, C1123.2, D1120.1 (A), D1126.1 (A), Q1112.2 (E), R1106.2, R1111.2, R1117.2, R1123.2, R1129.2, R1135.2, R1141.2, R1154.2, R1159.1, R1174.2, R1175.1, U1102.3 (GND2), U1107.1 (K)
CREF_PHCCH: R1168.2, R1169.1, U1105.2 (REF)
CREF_PHCCL: R1175.2, R1176.1, U1107.2 (REF)
D1_PHC: T1101.1 (D1), U1103.1 (D1)
D2_PHC: T1101.3 (D2), U1103.3 (D2)
DS1_CL: D1128.1 (K), D1129.2 (A)
DTB_CL: R1104.1, U1101.4 (Y)
DTS_CL: C1102.1, D1101.3 (K), R1103.2, U1101.2 (A)
DX_CL: D1124.3 (K), D1126.3 (COM), D1127.3 (K), R1161.1, U1102.2 (DESAT)
DY_CL: D1128.2 (A), R1161.2
EN5: U1102.14 (~RST/EN)
FLT_N: U1102.13 (~FLT)
GND: C1101.2, C1102.2, C1103.2, C1104.2, C1105.2, C1125.2, C1126.2, R1101.2, R1107.2, R1162.2, U1101.3 (GND), U1102.9 (GND1), U1103.4 (GND), U1103.6 (CLK)
G_CL1: C1111.1, D1102.3 (K), D1104.1 (K), Q1101.3 (D), R1108.2, R1109.2, R1110.1, R1113.2
G_CL2: C1113.1, D1105.3 (K), D1107.1 (K), Q1102.3 (D), R1114.2, R1115.2, R1116.1, R1119.2
G_CL3: C1115.1, D1108.3 (K), D1110.1 (K), Q1103.3 (D), R1120.2, R1121.2, R1122.1, R1125.2
G_CL4: C1117.1, D1111.3 (K), D1113.1 (K), Q1104.3 (D), R1126.2, R1127.2, R1128.1, R1131.2
G_CL5: C1119.1, D1114.3 (K), D1116.1 (K), Q1105.3 (D), R1132.2, R1133.2, R1134.1, R1137.2
G_CL6: C1121.1, D1117.3 (K), D1119.1 (K), Q1106.3 (D), R1138.2, R1139.2, R1140.1, R1143.2
INN_CL: C1104.1, R1104.2, U1102.11 (IN-)
INP_CL: C1101.1, R1102.2, U1102.10 (IN+)
KS_CL1: C1111.2, C1112.2, D1103.3 (K), R1110.2, R1111.1
KS_CL2: C1113.2, C1114.2, D1106.3 (K), R1116.2, R1117.1
KS_CL3: C1115.2, C1116.2, D1109.3 (K), R1122.2, R1123.1
KS_CL4: C1117.2, C1118.2, D1112.3 (K), R1128.2, R1129.1
KS_CL5: C1119.2, C1120.2, D1115.3 (K), R1134.2, R1135.1
KS_CL6: C1121.2, C1122.2, D1118.3 (K), R1140.2, R1141.1
NDB_CL: Q1114.1 (B), R1159.2
NDX_CL: D1127.1 (A), Q1114.3 (C), R1160.2
OUTH_CL: D1123.3 (K), R1108.1, R1114.1, R1120.1, R1126.1, R1132.1, R1138.1, R1146.1, U1102.4 (OUTH)
OUTL_CL: Q1108.1 (B), Q1109.1 (B), R1144.1, R1145.1, U1102.6 (OUTL)
P1_CL: R1105.1, R1106.1, U1102.1 (VEE2)
P16_CL: R1107.1, U1102.16 (TEST)
PWM5_5V: D1101.1 (A), R1103.1
PWM6_5V: R1101.1, R1102.1
QIB_CL: Q1110.1 (B), R1148.2, R1149.1
QID_CL: D1121.3 (K), R1149.2
QIZ_CL: D1121.1 (A), D1122.1 (A)
QRB_CL: C1124.2, Q1111.1 (B), R1151.1, R1152.2
QRZ_CL: C1124.1, D1123.1 (A), R1152.1
RAW_PHCCH: C1127.1, D1130.1 (K), D1131.1 (K), Q1115.1 (E), R1163.1
RAW_PHCCL: C1130.1, D1134.1 (K), D1135.1 (K), Q1116.1 (E), R1170.1
RB_PHCCH: Q1115.3 (B), R1163.2, R1164.1
RB_PHCCL: Q1116.3 (B), R1170.2, R1171.1
RDY: U1102.12 (RDY)
RK_PHCCH: C1128.1, R1164.2, U1104.1 (K)
RK_PHCCL: C1131.1, R1171.2, U1106.1 (K)
RREF_PHCCH: C1128.2, R1165.2, R1166.1, U1104.2 (REF)
RREF_PHCCL: C1131.2, R1172.2, R1173.1, U1106.2 (REF)
SA_PHCCH: D1130.2 (A), D1132.1 (K), T1101.4 (S1A)
SA_PHCCL: D1134.2 (A), D1136.1 (K), T1101.6 (S2A)
SB_CL: Q1107.3 (D), R1113.1, R1119.1, R1125.1, R1131.1, R1137.1, R1143.1
SB_PHCCH: D1131.2 (A), D1133.1 (K), T1101.5 (S1B)
SB_PHCCL: D1135.2 (A), D1137.1 (K), T1101.7 (S2B)
SK1_CL: Q1108.2 (E), R1109.1, R1115.1, R1121.1, R1144.2
SK2_CL: Q1109.2 (E), R1127.1, R1133.1, R1139.1, R1145.2
SW_C: D1129.1 (K)
VCG_CL: C1123.1, D1120.3 (K), Q1110.2 (E), R1147.2, R1148.1
VDD_CH: C1129.1, Q1115.2 (C), R1165.1, R1167.1
VDD_CL: C1106.1, C1107.1, C1132.1, D1126.2 (K), Q1113.2 (E), Q1116.2 (C), R1147.1, R1156.2, R1160.1, R1172.1, R1174.1, U1102.5 (VCC2)
VEEL1_CL: C1112.1, Q1101.2 (S), R1112.2
VEEL2_CL: C1114.1, Q1102.2 (S), R1118.2
VEEL3_CL: C1116.1, Q1103.2 (S), R1124.2
VEEL4_CL: C1118.1, Q1104.2 (S), R1130.2
VEEL5_CL: C1120.1, Q1105.2 (S), R1136.2
VEEL6_CL: C1122.1, Q1106.2 (S), R1142.2
VEE_CH: C1127.2, C1129.2, D1132.2 (A), D1133.2 (A), R1166.2, R1169.2, U1104.3 (A), U1105.3 (A)
VEE_CL: C1108.2, C1109.2, C1110.2, C1130.2, C1132.2, D1125.1 (A), D1136.2 (A), D1137.2 (A), Q1107.2 (S), Q1108.3 (C), Q1109.3 (C), Q1111.2 (E), Q1114.2 (E), R1105.2, R1112.1, R1118.1, R1124.1, R1130.1, R1136.1, R1142.1, R1150.2, R1151.2, R1158.2, R1173.2, R1176.2, U1102.8 (VEE2), U1106.3 (A), U1107.3 (A)
ZM1_CL: D1102.1 (A), D1103.1 (A)
ZM2_CL: D1105.1 (A), D1106.1 (A)
ZM3_CL: D1108.1 (A), D1109.1 (A)
ZM4_CL: D1111.1 (A), D1112.1 (A)
ZM5_CL: D1114.1 (A), D1115.1 (A)
ZM6_CL: D1117.1 (A), D1118.1 (A)

Notes on the sheet:
PHC: GATE BIAS (PER PHASE)
CL: DESAT
DESAT pin (internal 500 uA blanking source, trip 8.5-10.0 V) - Rs - 2 x BYG23T-M3/TR (1300 V each) - drain. BAT54S keeps DX between COM and VDD against dv/dt through the string; Cblk footprint DNP.
Per device: Ron/Roff, 0.5R Kelvin R to the COM star, 10k and Zeners (about +21 V / -5.7 V) on its own Kelvin net. Miller hold: N-MOSFET clamp (PMV30ENEA) gate-pin to a local VEE (1u on the Kelvin pin). LAYOUT: FET + 1u at the device, loop <= 1 nH.
MMBT3906 inverter (E COM, base BAT54+2.2k on CLAMP) drives CG to COM once the lowest gate is below ~-1.2 V; MMBT3904 release (from OUTH via 5.6 V Zener) holds CG at VEE while OUTH drives.
Gate and Kelvin of each device as coupled pairs of equal length from the COM star; Ron, Roff, Kelvin R, 10k + 1n, Zeners and the clamp FET + C_VL at each device (loop <= 1 nH). PNP followers next to their three gates. DESAT string >= 2.5 mm pad gap per diode; coat to PD1. Miller hold of six gates N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
CL: TURN-OFF BUFFER
CL: DRIVER AND 6 GATES
DESAT > 10.3-10.9 V (above the 10.0 V maximum trip of the -Q1 grade) -> MMBT3904 -> MMBT3906 charges BG to VEE + 10 V; per device AO3400A + 22R pull the gate to VEE; BG holds ~3 us (1k + FET gates).
2 x ZXTP25040DFH emitter followers on OUTL (B-E 1k, C to VEE): each sinks the Roff current of 3 gates; the NSI6651 supplies base current only. Turn-on stays on OUTH.
SN6505B push-pull 420 kHz from +5V_GD, BIAS_EN high = on; T_BIAS4 custom, functional insulation (PD-free >= 1.75 kVpk, <= 5 pF per secondary). Per channel: bridge, PNP regulator VDD-VEE, ATL431 COM split.
IN+ = own PWM; IN- = complementary switch, falling edge stretched 3.65k/100p (interlock + min dead time = max(firmware, hardware)). Bias PG (active low) pulls RDY low.
CL: MILLER CLAMP CONTROL
LEG C: LAYOUT RULES
CL: LOGIC SIDE
CL: SHORT-CIRCUIT BOOSTER
