vectivolt/PCM/hardware/PCS-PWR/sheets/12_filta.kicad_sch

## KiCad design hardware/PCS-PWR/sheets/12_filta.kicad_sch (2026-10-06)

Schematic: 12_filta.kicad_sch

Parts:
C1201: 100n 50V
C1202, C1203: 1n 50V
C1204, C1205: 25u 450VAC RFQ
C1206: 10u 450VAC RFQ
CS1201: STK-250HO/4; MPN STK-250HO/4
J1201, J1202, J1203, J1204, J1205, J1206, J1207, J1208, J1209, J1210, J1211, J1212, J1213: 7461057; MPN 7461057
L1201: L1 120u (CUSTOM)
L1202: L2 6u (CUSTOM)
R1201, R1202: 100R
R1203: 2R 25W RFQ

Connections:
+5V: C1201.1, CS1201.1 (+UC)
AC_T_A: J1213.1
AGND: C1201.2, C1202.2, C1203.2, CS1201.2 (GND), L1201.4 (NTC2)
F_A: C1204.1, C1205.1, C1206.1, CS1201.P, J1204.1, J1205.1, J1206.1, J1207.1, J1208.1, J1209.1, L1201.2 (B), L1202.1 (A)
IL1: C1202.1, R1201.2
IL1R: C1203.1, R1202.2
IL1R_S: CS1201.4 (UREF), R1202.1
IL1_S: CS1201.3 (UOUT), R1201.1
L2O_A: J1210.1, J1211.1, J1212.1, L1202.2 (B)
M: C1204.2, C1205.2, R1203.2
NTC5: L1201.3 (NTC1)
PE: L1201.5 (CORE), L1202.3 (CORE)
RD_A: C1206.2, R1203.1
SW_A: J1201.1, J1202.1, J1203.1, L1201.1 (A)

Notes on the sheet:
PHASE A: L1 AND L2 (CHASSIS, CUSTOM) AND THEIR STUDS
IL1 = Uref + 3.2 mV/A x I (I + = L1 -> C_f: body arrow, verify at incoming inspection), IL1R = its Uref pin; 100R + 1 nF each at the source (as PV-PWR). Primary = L1's output busbar through the aperture (a 50 Hz-smooth node, not the switch node). OCD (open drain, 2.93 x I_PN = 732 A +/-10 %) not us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
PHASE A CURRENT SENSOR STK-250HO/4 (C_F SIDE OF L1)
PHASE A C_F AND DAMPING BRANCH (STAR = M, THE DC MIDPOINT)
Board studs (REDCUBE press-fit, 100 A each): 3 x switch node to L1, 3 x L1 out (C_f node, its busbar through the sensor), 3 x C_f node to L2, 3 x L2 out (to AC contactor K1 on the port sheet). Cores bonded to PE.
C_f = 2 x 25 uF MKP (50 uF); R_d 2 ohm + C_d 10 uF in series, F_A to M.
