vectivolt/PCM/hardware/PCS-PWR/sheets/13_filtb.kicad_sch

## KiCad design hardware/PCS-PWR/sheets/13_filtb.kicad_sch (2026-10-06)

Schematic: 13_filtb.kicad_sch

Parts:
C1301: 100n 50V
C1302, C1303: 1n 50V
C1304, C1305: 25u 450VAC RFQ
C1306: 10u 450VAC RFQ
CS1301: STK-250HO/4; MPN STK-250HO/4
J1301, J1302, J1303, J1304, J1305, J1306, J1307, J1308, J1309, J1310, J1311, J1312, J1313: 7461057; MPN 7461057
L1301: L1 120u (CUSTOM)
L1302: L2 6u (CUSTOM)
R1301, R1302: 100R
R1303: 2R 25W RFQ

Connections:
+5V: C1301.1, CS1301.1 (+UC)
AC_T_B: J1313.1
AGND: C1301.2, C1302.2, C1303.2, CS1301.2 (GND), L1301.4 (NTC2)
F_B: C1304.1, C1305.1, C1306.1, CS1301.P, J1304.1, J1305.1, J1306.1, J1307.1, J1308.1, J1309.1, L1301.2 (B), L1302.1 (A)
IL2: C1302.1, R1301.2
IL2R: C1303.1, R1302.2
IL2R_S: CS1301.4 (UREF), R1302.1
IL2_S: CS1301.3 (UOUT), R1301.1
L2O_B: J1310.1, J1311.1, J1312.1, L1302.2 (B)
M: C1304.2, C1305.2, R1303.2
NTC6: L1301.3 (NTC1)
PE: L1301.5 (CORE), L1302.3 (CORE)
RD_B: C1306.2, R1303.1
SW_B: J1301.1, J1302.1, J1303.1, L1301.1 (A)

Notes on the sheet:
PHASE B C_F AND DAMPING BRANCH (STAR = M, THE DC MIDPOINT)
PHASE B CURRENT SENSOR STK-250HO/4 (C_F SIDE OF L1)
C_f = 2 x 25 uF MKP (50 uF); R_d 2 ohm + C_d 10 uF in series, F_B to M.
PHASE B: L1 AND L2 (CHASSIS, CUSTOM) AND THEIR STUDS
Board studs (REDCUBE press-fit, 100 A each): 3 x switch node to L1, 3 x L1 out (C_f node, its busbar through the sensor), 3 x C_f node to L2, 3 x L2 out (to AC contactor K1 on the port sheet). Cores bonded to PE.
IL2 = Uref + 3.2 mV/A x I (I + = L1 -> C_f: body arrow, verify at incoming inspection), IL2R = its Uref pin; 100R + 1 nF each at the source (as PV-PWR). Primary = L1's output busbar through the aperture (a 50 Hz-smooth node, not the switch node). OCD (open drain, 2.93 x I_PN = 732 A +/-10 %) not us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
