vectivolt/PCM/hardware/PCS-PWR/sheets/14_filtc.kicad_sch

## KiCad design hardware/PCS-PWR/sheets/14_filtc.kicad_sch (2026-10-06)

Schematic: 14_filtc.kicad_sch

Parts:
C1401: 100n 50V
C1402, C1403: 1n 50V
C1404, C1405: 25u 450VAC RFQ
C1406: 10u 450VAC RFQ
CS1401: STK-250HO/4; MPN STK-250HO/4
J1401, J1402, J1403, J1404, J1405, J1406, J1407, J1408, J1409, J1410, J1411, J1412, J1413: 7461057; MPN 7461057
L1401: L1 120u (CUSTOM)
L1402: L2 6u (CUSTOM)
R1401, R1402: 100R
R1403: 2R 25W RFQ

Connections:
+5V: C1401.1, CS1401.1 (+UC)
AC_T_C: J1413.1
AGND: C1401.2, C1402.2, C1403.2, CS1401.2 (GND), L1401.4 (NTC2)
F_C: C1404.1, C1405.1, C1406.1, CS1401.P, J1404.1, J1405.1, J1406.1, J1407.1, J1408.1, J1409.1, L1401.2 (B), L1402.1 (A)
IL3: C1402.1, R1401.2
IL3R: C1403.1, R1402.2
IL3R_S: CS1401.4 (UREF), R1402.1
IL3_S: CS1401.3 (UOUT), R1401.1
L2O_C: J1410.1, J1411.1, J1412.1, L1402.2 (B)
M: C1404.2, C1405.2, R1403.2
NTC7: L1401.3 (NTC1)
PE: L1401.5 (CORE), L1402.3 (CORE)
RD_C: C1406.2, R1403.1
SW_C: J1401.1, J1402.1, J1403.1, L1401.1 (A)

Notes on the sheet:
C_f = 2 x 25 uF MKP (50 uF); R_d 2 ohm + C_d 10 uF in series, F_C to M.
IL3 = Uref + 3.2 mV/A x I (I + = L1 -> C_f: body arrow, verify at incoming inspection), IL3R = its Uref pin; 100R + 1 nF each at the source (as PV-PWR). Primary = L1's output busbar through the aperture (a 50 Hz-smooth node, not the switch node). OCD (open drain, 2.93 x I_PN = 732 A +/-10 %) not us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
PHASE C CURRENT SENSOR STK-250HO/4 (C_F SIDE OF L1)
PHASE C: L1 AND L2 (CHASSIS, CUSTOM) AND THEIR STUDS
Board studs (REDCUBE press-fit, 100 A each): 3 x switch node to L1, 3 x L1 out (C_f node, its busbar through the sensor), 3 x C_f node to L2, 3 x L2 out (to AC contactor K1 on the port sheet). Cores bonded to PE.
PHASE C C_F AND DAMPING BRANCH (STAR = M, THE DC MIDPOINT)
