vectivolt/PCM/hardware/PCS-PWR/sheets/15_acsense.kicad_sch

## KiCad design hardware/PCS-PWR/sheets/15_acsense.kicad_sch (2026-10-06)

Schematic: 15_acsense.kicad_sch

Parts:
C1501, C1502, C1503, C1504, C1505, C1506: 4.7n 50V
C1507, C1508, C1509: 100n 50V
R1501, R1502, R1503, R1504, R1505, R1506, R1508, R1509, R1510, R1511, R1512, R1513, R1515, R1516, R1517, R1518, R1519, R1520, R1522, R1523, R1524, R1525, R1526, R1527, R1529, R1530, R1531, R1532, R1533, R1534, R1536, R1537, R1538, R1539, R1540, R1541: 1M; MPN ARHV06BTC1004A
R1507, R1514, R1521, R1528, R1535, R1542: 4.99k; MPN TNPW12064K99BEEA
U1501, U1502, U1503: OPA2388IDR; MPN OPA2388IDR

Connections:
+3V3: C1507.1, C1508.1, C1509.1, U1501.8 (V+), U1502.8 (V+), U1503.8 (V+)
AC_T_A: R1508.1
AC_T_B: R1522.1
AC_T_C: R1536.1
AGND: C1507.2, C1508.2, C1509.2, U1501.4 (V-), U1502.4 (V-), U1503.4 (V-)
D_VMID: C1501.2, C1502.2, C1503.2, C1504.2, C1505.2, C1506.2, R1507.2, R1514.2, R1521.2, R1528.2, R1535.2, R1542.2
F_A: R1501.1
F_B: R1515.1
F_C: R1529.1
VC1: U1501.1 (OUTA), U1501.2 (-INA)
VC1_D: C1501.1, R1506.2, R1507.1, U1501.3 (+INA)
VC1_D_1: R1501.2, R1502.1
VC1_D_2: R1502.2, R1503.1
VC1_D_3: R1503.2, R1504.1
VC1_D_4: R1504.2, R1505.1
VC1_D_5: R1505.2, R1506.1
VC2: U1502.1 (OUTA), U1502.2 (-INA)
VC2_D: C1503.1, R1520.2, R1521.1, U1502.3 (+INA)
VC2_D_1: R1515.2, R1516.1
VC2_D_2: R1516.2, R1517.1
VC2_D_3: R1517.2, R1518.1
VC2_D_4: R1518.2, R1519.1
VC2_D_5: R1519.2, R1520.1
VC3: U1503.1 (OUTA), U1503.2 (-INA)
VC3_D: C1505.1, R1534.2, R1535.1, U1503.3 (+INA)
VC3_D_1: R1529.2, R1530.1
VC3_D_2: R1530.2, R1531.1
VC3_D_3: R1531.2, R1532.1
VC3_D_4: R1532.2, R1533.1
VC3_D_5: R1533.2, R1534.1
VG1: U1501.6 (-INB), U1501.7 (OUTB)
VG1_D: C1502.1, R1513.2, R1514.1, U1501.5 (+INB)
VG1_D_1: R1508.2, R1509.1
VG1_D_2: R1509.2, R1510.1
VG1_D_3: R1510.2, R1511.1
VG1_D_4: R1511.2, R1512.1
VG1_D_5: R1512.2, R1513.1
VG2: U1502.6 (-INB), U1502.7 (OUTB)
VG2_D: C1504.1, R1527.2, R1528.1, U1502.5 (+INB)
VG2_D_1: R1522.2, R1523.1
VG2_D_2: R1523.2, R1524.1
VG2_D_3: R1524.2, R1525.1
VG2_D_4: R1525.2, R1526.1
VG2_D_5: R1526.2, R1527.1
VG3: U1503.6 (-INB), U1503.7 (OUTB)
VG3_D: C1506.1, R1541.2, R1542.1, U1503.5 (+INB)
VG3_D_1: R1536.2, R1537.1
VG3_D_2: R1537.2, R1538.1
VG3_D_3: R1538.2, R1539.1
VG3_D_4: R1539.2, R1540.1
VG3_D_5: R1540.2, R1541.1

Notes on the sheet:
DIVIDERS (1 V = 1203 V AROUND VMID, BIPOLAR: THE TERMINALS FLOAT AGAINST DC- WITH THE CONTACTORS OPEN)
Relay test: VG vs VC per phase with one contactor closed at a time (firmware).
