vectivolt/PCM/hardware/PCS-PWR/sheets/16_leanB_power.kicad_sch

## KiCad design hardware/PCS-PWR/sheets/16_leanB_power.kicad_sch (2026-10-06)

Schematic: 16_leanB_power.kicad_sch

Parts:
C1701: 470p 50V
C1702: 1n 50V
C1703, C1704, C1705, C1706, C1707, C1710, C1711, C1712, C1713, C1714, C1802, C1803, C1804, C1805: 100n 50V
C1708, C1709: 4.7n 50V
C1801: 1u 50V
D1601: BAS16; MPN BAS16
D1801: BZX84-C15; MPN BZX84-C15
D1802, D1804: SMBJ33A; MPN SMBJ33A
D1803, D1805: S2M-13-F; MPN S2M-13-F
F1601, F1602: 36A gPV 14x51; MPN 002637115
F1603, F1604: HCHVF1000-400A-38R; MPN HCHVF1000-400A-38R
K1801: HFE82V-300C/1000-24-H-C5-1; MPN HFE82V-300C/1000-24-H-C5-1
K1802: G7L-2A-X DC24; MPN G7L-2A-X DC24
Q1801: PMV30ENEAR; MPN PMV30ENEAR
Q1802, Q1804: BSS138BK; MPN BSS138BK
Q1803, Q1805: IRFR9214TRPbF; MPN IRFR9214TRPbF
R1601, R1602, R1603, R1604, R1605, R1606, R1607, R1608, R1609, R1610, R1611, R1612: 82.5k
R1613: 220k
R1701, R1703, R1705, R1707, R1723, R1725: 1.00k
R1702, R1704: 30.1k
R1706, R1708: 10.0k
R1709, R1710, R1711, R1712, R1713, R1714, R1716, R1717, R1718, R1719, R1720, R1721: 1M; MPN ARHV06BTC1004A
R1715, R1722: 4.99k; MPN TNPW12064K99BEEA
R1724, R1726: 20.0k
R1801, R1802, R1803, R1804: 37.4
R1805: 56k
R1806, R1807, R1811, R1812: 100k
R1808, R1809, R1813, R1814: 10k
R1810: 220R RFQ
RS1701, RS1702: 0.2m; MPN CSS2H-3920R-L200F
RV1601, RV1602, RV1603: TVT25751KFKG; MPN TVT25751KFKG
U1601: CNY65B; MPN CNY65B
U1701, U1706, U1707: OPA2388IDR; MPN OPA2388IDR
U1702, U1704, U1708, U1709: TLV3502AIDCNR; MPN TLV3502AIDCNR
U1703, U1705, U1803: SN74LVC1G32DBVR; MPN SN74LVC1G32DBVR
U1710, U1801, U1802, U1804: SN74LVC1G11DBVR; MPN SN74LVC1G11DBVR
X1601, X1602, X1603, X1604: 006710340; MPN 006710340

Connections:
+3V3: C1703.1, C1704.1, C1705.1, C1706.1, C1707.1, C1710.1, C1711.1, C1712.1, C1713.1, C1714.1, C1802.1, C1803.1, C1804.1, C1805.1, R1613.1, U1701.8 (V+), U1702.8 (V+), U1703.5 (VCC), U1704.8 (V+), U1705.5 (VCC), U1706.8 (V+), U1707.8 (V+), U1708.8 (V+), U1709.4 (-INB), U1709.8 (V+), U1710.5 (VCC), U1710.6 (C), U1801.5 (VCC), U1802.5 (VCC), U1802.6 (C), U1803.5 (VCC), U1804.5 (VCC), U1804.6 (C)
+24V: Q1803.3 (S), Q1805.3 (S), R1809.1, R1814.1
AGND: C1703.2, C1704.2, C1705.2, C1706.2, C1707.2, C1710.2, C1711.2, C1712.2, C1713.2, C1714.2, C1802.2, C1803.2, C1804.2, C1805.2, U1601.3 (E), U1701.4 (V-), U1702.5 (V-), U1703.3 (GND), U1704.5 (V-), U1705.3 (GND), U1706.4 (V-), U1707.4 (V-), U1707.5 (+INB), U1708.5 (V-), U1709.3 (+INB), U1709.5 (V-), U1710.2 (GND), U1801.2 (GND), U1802.2 (GND), U1803.3 (GND), U1804.2 (GND)
B_DVA: R1726.2, U1707.1 (OUTA), U1708.3 (+INB), U1709.2 (-INA)
B_DVHI: U1709.7 (OUTA), U1710.3 (B)
B_DVLO: U1708.6 (OUTB), U1710.1 (A)
B_DVN: R1725.2, R1726.1, U1707.2 (-INA)
B_DVP: R1723.2, R1724.1, U1707.3 (+INA)
B_DV_OK: U1710.4 (Y), U1801.6 (C)
B_HOLD: U1703.4 (Y), U1802.1 (A)
B_HOLDN: U1702.6 (OUTB), U1703.2 (B)
B_HOLDP: U1702.7 (OUTA), U1703.1 (A)
B_IH: C1702.2, R1708.2, U1701.7 (OUTB), U1702.1 (+INA), U1702.4 (-INB), U1704.1 (+INA), U1704.4 (-INB)
B_IM: C1701.2, R1704.2, U1701.1 (OUTA)
B_IN+: F1601.1, F1603.1, X1601.1
B_IN-: F1602.1, F1604.1, X1603.1
B_K_COIL: C1801.1, D1802.2 (A), K1801.1 (COIL1), Q1803.2 (D)
B_K_G: Q1802.1 (G), R1807.1, U1802.3 (B), U1803.4 (Y)
B_K_GB: C1801.2, D1801.3 (K), Q1801.1 (G), R1805.1
B_K_H1: R1801.2, R1802.1
B_K_H2: R1802.2, R1803.1
B_K_H3: R1803.2, R1804.1, U1801.4 (Y), U1803.1 (A)
B_K_HG: U1802.4 (Y), U1803.2 (B)
B_K_LO: K1801.2 (COIL2), Q1801.3 (D), R1801.1
B_K_PD: Q1802.3 (D), R1808.1
B_K_PG: Q1803.1 (G), R1808.2, R1809.2
B_K_Z: D1802.1 (K), D1803.1 (K)
B_MON1: R1601.1, RV1601.3 (MON)
B_MON2: R1612.2, RV1602.3 (MON)
B_MON3: D1601.1 (A), RV1603.3 (MON), U1601.2 (K)
B_MONA: D1601.3 (K), R1606.2, U1601.1 (A)
B_MR1: R1601.2, R1602.1
B_MR2: R1602.2, R1603.1
B_MR3: R1603.2, R1604.1
B_MR4: R1604.2, R1605.1
B_MR5: R1605.2, R1606.1
B_MS1: R1607.2, R1608.1
B_MS2: R1608.2, R1609.1
B_MS3: R1609.2, R1610.1
B_MS4: R1610.2, R1611.1
B_MS5: R1611.2, R1612.1
B_OC: U1705.4 (Y)
B_OCN: U1704.6 (OUTB), U1705.2 (B)
B_OCP: U1704.7 (OUTA), U1705.1 (A)
B_POL_OK: U1708.7 (OUTA), U1801.3 (B), U1804.3 (B)
B_PRE_M: K1802.4 (P2), K1802.6 (P1)
B_PRE_R: K1802.2 (P2-), R1810.1
B_P_COIL: D1804.2 (A), K1802.1 (COIL), Q1805.2 (D)
B_P_G: Q1804.1 (G), R1812.1, U1804.4 (Y)
B_P_PD: Q1804.3 (D), R1813.1
B_P_PG: Q1805.1 (G), R1813.2, R1814.2
B_P_Z: D1804.1 (K), D1805.1 (K)
B_SHAN: C1701.1, R1703.2, R1704.1, U1701.2 (-INA)
B_SHAP: R1701.2, R1702.1, U1701.3 (+INA)
B_SHBN: C1702.1, R1707.2, R1708.1, U1701.6 (-INB)
B_SHBP: R1705.2, R1706.1, U1701.5 (+INB)
B_SP+: F1601.2, RV1601.1 (L), X1602.1
B_SP-: F1602.2, RV1602.1 (L), X1604.1
B_SPAREB: U1707.6 (-INB), U1707.7 (OUTB)
B_SPD_N: R1613.2, U1601.4 (C)
B_SPM: R1607.1, RV1601.2 (N), RV1602.2 (N), RV1603.1 (L)
B_T+: F1603.2, K1801.A1, K1802.8 (P1+), R1709.1
B_T-: F1604.2, R1701.1, R1705.1, RS1701.1, RS1702.1
B_VBD: C1709.1, R1721.2, R1722.1, U1706.5 (+INB)
B_VBD_1: R1716.2, R1717.1
B_VBD_2: R1717.2, R1718.1
B_VBD_3: R1718.2, R1719.1
B_VBD_4: R1719.2, R1720.1
B_VBD_5: R1720.2, R1721.1
B_VB_O: R1725.1, U1706.6 (-INB), U1706.7 (OUTB)
B_VXD: C1708.1, R1714.2, R1715.1, U1706.3 (+INA)
B_VXD_1: R1709.2, R1710.1
B_VXD_2: R1710.2, R1711.1
B_VXD_3: R1711.2, R1712.1
B_VXD_4: R1712.2, R1713.1
B_VXD_5: R1713.2, R1714.1
B_VX_O: R1723.1, U1706.1 (OUTA), U1706.2 (-INA), U1708.1 (+INA)
DC+: K1801.A2, R1716.1, R1810.2
DC-: R1703.1, R1707.1, RS1701.2, RS1702.2
D_HOLD_HI: U1702.2 (-INA)
D_HOLD_LO: U1702.3 (+INB)
D_OC_HI: U1704.2 (-INA)
D_OC_LO: U1704.3 (+INB)
D_TH_HI: U1708.2 (-INA), U1709.1 (+INA)
D_TH_LO: U1708.4 (-INB)
D_VMID: C1708.2, C1709.2, R1702.2, R1706.2, R1715.2, R1722.2, R1724.2
GND: D1801.1 (A), D1803.2 (A), D1805.2 (A), K1802.0 (COIL), Q1801.2 (S), Q1802.2 (S), Q1804.2 (S), R1804.2, R1805.2, R1806.2, R1807.2, R1811.2, R1812.2
K_B: R1806.1, U1801.1 (A)
K_PRE: R1811.1, U1804.1 (A)
PE_T: RV1603.2 (N)

Notes on the sheet:
PORT B (BATTERY SOURCE), D-044 LEAN PORT
TVT25751 x 3 (615 VDC, thermal link + monitor lead): MOV1 +/M, MOV2 -/M, MOV3 M/PE_T. Up,eff 3793 V pole-PE and pole-pole at In 3 kA (calc., <= 4.0 kV -> reinforced 6 kV / basic 4 kV, D-032); Imax 25 kA. Branch fuses ETI CH14x51 gPV 36 A 30 kA (L/R 2 ms). Monitor loop through both fuses and all thr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
ON-BOARD SURGE PROTECTION: VARISTOR Y (IC-01, IC-12)
AR FUSES (BATTERY-TYPE PORT)
Terminal side B_IN+ / B_IN-, bank DC+. HCHVF1000-400A-38R aR in both poles. Contactor opens <= 0.97 kA, held above (port_spec lean). Fuse / contactor coordination: the board's design check.
HCHVF1000-400A-38R in both poles (aR, partial range): see the board's design check.
