vectivolt/PCM/hardware/PCS-PWR/sheets/19_dcterm.kicad_sch

## KiCad design hardware/PCS-PWR/sheets/19_dcterm.kicad_sch (2026-10-07)

Schematic: 19_dcterm.kicad_sch

Parts:
C1901: X 2.2u 1300V RFQ
C1902, C1903: VY1472M63Y5UQ63V0; MPN VY1472M63Y5UQ63V0
C1904: 4.7n 50V
C1905: 100n 50V
J1901: DC terminal B+ 250 A (CUSTOM)
J1902: DC terminal B- 250 A (CUSTOM)
J1903, J1904, J1905, J1906, J1907, J1908, J1909, J1910, J1911: 7461057; MPN 7461057
L1901: N-C-644025; MPN N-C-644025
LK1901: PE_T link to chassis PE: removable strap, OPEN fo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
MH1901: PE bond M4 (IMD divider reference)
Q1901, Q1902, Q1903, Q1904: BSS138BK; MPN BSS138BK
R1901: 10k
R1902, R1903, R1904, R1905, R1906, R1907: 1M; MPN ARHV06BTC1004A
R1908: 4.99k; MPN TNPW12064K99BEEA
R1909, R1910, R1911, R1912, R1913, R1914, R1915, R1916, R1919, R1920, R1921, R1922, R1923, R1924, R1925, R1926: 124k; MPN ARHV13BTC1243A
R1917, R1927: 330R
R1918, R1928: 100k
U1901: OPA2388IDR; MPN OPA2388IDR
U1902, U1903: CA-IS3417WT; MPN CA-IS3417WT

Connections:
+3V3: C1905.1, R1901.1, U1901.8 (V+)
+5V: R1917.1, R1927.1
AGND: C1905.2, U1901.4 (V-), U1901.5 (+INB)
B_IN+: C1901.1, C1902.1, J1909.1, L1901.2 (A2), R1909.1
B_IN-: C1901.2, C1903.1, J1910.1, L1901.4 (B2)
B_OC: Q1902.1 (G)
B_SPD_N: Q1901.1 (G)
B_T+: J1911.1
B_T-: J1906.1, J1907.1, J1908.1
B_TERM+: J1901.1, L1901.1 (A1)
B_TERM-: J1902.1, L1901.3 (B1)
DC+: J1903.1, J1904.1, J1905.1
DC-: R1919.1
D_VMID: C1904.2, R1908.2
FLT_N: Q1902.3 (D)
GND: Q1901.2 (S), Q1902.2 (S), Q1903.2 (S), Q1904.2 (S), R1918.2, R1928.2
IMDN_A: R1927.2, U1903.4 (ANODE)
IMDN_K: Q1904.3 (D), U1903.3 (CATHODE1), U1903.5 (CATHODE2)
IMDN_R1: R1919.2, R1920.1
IMDN_R2: R1920.2, R1921.1
IMDN_R3: R1921.2, R1922.1
IMDN_R4: R1922.2, R1923.1
IMDN_R5: R1923.2, R1924.1
IMDN_R6: R1924.2, R1925.1
IMDN_R7: R1925.2, R1926.1
IMDN_S: R1926.2, U1903.11 (Drain1), U1903.12 (Drain1)
IMDP_A: R1917.2, U1902.4 (ANODE)
IMDP_K: Q1903.3 (D), U1902.3 (CATHODE1), U1902.5 (CATHODE2)
IMDP_R1: R1909.2, R1910.1
IMDP_R2: R1910.2, R1911.1
IMDP_R3: R1911.2, R1912.1
IMDP_R4: R1912.2, R1913.1
IMDP_R5: R1913.2, R1914.1
IMDP_R6: R1914.2, R1915.1
IMDP_R7: R1915.2, R1916.1
IMDP_S: R1916.2, U1902.11 (Drain1), U1902.12 (Drain1)
IMD_AUXD: C1904.1, R1907.2, R1908.1, U1901.3 (+INA)
IMD_AUXD_1: R1902.2, R1903.1
IMD_AUXD_2: R1903.2, R1904.1
IMD_AUXD_3: R1904.2, R1905.1
IMD_AUXD_4: R1905.2, R1906.1
IMD_AUXD_5: R1906.2, R1907.1
IMD_AUX_O: U1901.1 (OUTA), U1901.2 (-INA)
IMD_SPARE: U1901.6 (-INB), U1901.7 (OUTB)
IMD_SW1: Q1903.1 (G), R1918.1
IMD_SW2: Q1904.1 (G), R1928.1
MOV_OK: Q1901.3 (D), R1901.2
PE: LK1901.2 (PE)
PE_D: MH1901.1, R1902.1
PE_T: C1902.2, C1903.2, LK1901.1 (PE_T), U1902.9 (Drain2), U1902.10 (Drain2), U1903.9 (Drain2), U1903.10 (Drain2)

Notes on the sheet:
DC TERMINALS AND FILTER
B_TERM+/- (250 A), X 2.2 uF 1300 V across the port, Y1 4.7 nF pole - PE_T (removable PE link for the hipot). Board taps B_IN+ / B_IN- by short links.
HOLD = B_HOLD (|I| >= 0.97-1.03 kA: contactor held). MOV_OK high while the varistor monitor loop conducts. Port over-current (387-413 A) pulls FLT_N low (open drain): the latch trips without firmware.
Battery side, contactors open (IEC 62109-2 style check before connecting): IMD_SW1 = string B_IN+ -> PE, IMD_SW2 = PE -> DC-; VPE to PCS_PC.
PE_T (Y capacitors, MOV3, IMD strings) reaches PE through a removable strap (open for the hipot).
PORT STATUS TO PCS_PC
INSULATION MONITOR (PORT.LEAN_IMD)
