vectivolt/PCM/hardware/PCS-PWR/sheets/20_acport.kicad_sch

## KiCad design hardware/PCS-PWR/sheets/20_acport.kicad_sch (2026-10-07)

Schematic: 20_acport.kicad_sch

Parts:
C2001, C2002, C2003: VY1472M63Y5UQ63V0; MPN VY1472M63Y5UQ63V0
C2004: 1n 50V
C2005: 100n 50V
CS2001: RCM type B RFQ
D2001, D2003: SMBJ33A; MPN SMBJ33A
D2002, D2004: S2M-13-F; MPN S2M-13-F
J2001: AC terminal L1 250 A (CUSTOM)
J2002: AC terminal L2 250 A (CUSTOM)
J2003: AC terminal L3 250 A (CUSTOM)
K2001: K1 AC-1 250A RFQ
K2002: K2 AC-1 250A RFQ
L2001: CM choke (CUSTOM)
Q2001, Q2003: BSS138BK; MPN BSS138BK
Q2002, Q2004: IRFR9214TRPbF; MPN IRFR9214TRPbF
R2001, R2004: 100k
R2002, R2003, R2005, R2006: 10k
R2007: 100R
RV2001, RV2002, RV2003: TVT25751KFKG; MPN TVT25751KFKG
TP2001, TP2002, TP2003: TP

Connections:
+5V: C2005.1, CS2001.1 (VCC)
+24V: Q2002.3 (S), Q2004.3 (S), R2003.1, R2006.1
AC_K1_COIL: D2001.2 (A), K2001.7 (A1), Q2002.2 (D)
AC_K1_PD: Q2001.3 (D), R2002.1
AC_K1_PG: Q2002.1 (G), R2002.2, R2003.2
AC_K1_Z: D2001.1 (K), D2002.1 (K)
AC_K2_COIL: D2003.2 (A), K2002.7 (A1), Q2004.2 (D)
AC_K2_PD: Q2003.3 (D), R2005.1
AC_K2_PG: Q2004.1 (G), R2005.2, R2006.2
AC_K2_Z: D2003.1 (K), D2004.1 (K)
AC_T_A: C2001.1, J2001.1, L2001.2 (A2), RV2001.1 (L)
AC_T_B: C2002.1, J2002.1, L2001.4 (B2), RV2002.1 (L)
AC_T_C: C2003.1, J2003.1, L2001.6 (C2), RV2003.1 (L)
AGND: C2004.2, C2005.2, CS2001.2 (GND)
GND: D2002.2 (A), D2004.2 (A), K2001.8 (A2), K2002.8 (A2), Q2001.2 (S), Q2003.2 (S), R2001.2, R2004.2
K2O_A: K2002.2 (T1), L2001.1 (A1)
K2O_B: K2002.4 (T2), L2001.3 (B1)
K2O_C: K2002.6 (T3), L2001.5 (C1)
KM_A: K2001.2 (T1), K2002.1 (L1)
KM_B: K2001.4 (T2), K2002.3 (L2)
KM_C: K2001.6 (T3), K2002.5 (L3)
K_A: Q2001.1 (G), R2001.1
K_AC2: Q2003.1 (G), R2004.1
L2O_A: K2001.1 (L1)
L2O_B: K2001.3 (L2)
L2O_C: K2001.5 (L3)
MOV_AC_A: RV2001.3 (MON), TP2001.1
MOV_AC_B: RV2002.3 (MON), TP2002.1
MOV_AC_C: RV2003.3 (MON), TP2003.1
PE_T: C2001.2, C2002.2, C2003.2, RV2001.2 (N), RV2002.2 (N), RV2003.2 (N)
RCM: C2004.1, R2007.2
RCM_S: CS2001.3 (OUT), R2007.1
RCM_TST: CS2001.4 (TEST)

Notes on the sheet:
Relay test before every connection: K1 alone, then K2 alone; the voltage across the open one is VG - VC (stage-3 dividers). Close only after synchronisation, open only at zero current (firmware).
K1 from K_A (= K_AC1), K2 from K_AC2; logic lost = coil off. The contactors' DC coil modules economise.
AC SURGE PROTECTION (TYPE II) AND Y1
CM CHOKE (CHASSIS, CUSTOM) AND AC TERMINALS
AC CONTACTORS K1, K2 (CHASSIS, RFQ): TWO 3-POLE CONTACTORS IN SERIES
COIL DRIVERS (PORT._LEAN_DRV): BSS138 -> IRFR9214 FROM THE LIVE 24 V, S2M + SMBJ33A CLAMP
Around L1-L3 between the CM choke and the terminals; RCM analog out and RCM_TST to PCS_X.
One turn of the three phase busbars through the cores; terminals L1-L3 250 A; PE terminal on the chassis.
Per phase a thermally protected varistor TVT25751 (465 V AC) and a Y1 4.7 nF to PE_T; the removable PE link opens them for the hipot. Monitor leads to test points (OPEN 5).
RESIDUAL-CURRENT SENSOR (TYPE B, RFQ)
