vectivolt/PCM/hardware/PCS-PWR/sheets/21_pe.kicad_sch

## KiCad design hardware/PCS-PWR/sheets/21_pe.kicad_sch (2026-10-06)

Schematic: 21_pe.kicad_sch

Parts:
C2101, C2102, C2103, C2104, C2105, C2106: 100n 50V
HS2101: heatsink section a (CUSTOM)
HS2102: heatsink section b (CUSTOM)
HS2103: heatsink section c (CUSTOM)
J2101, J2102, J2103, J2104, J2105, J2106: KF2EDGR-3.5-2P; MPN KF2EDGR-3.5-2P
MH2101: PE bond M4 (board PE)
RT2101, RT2102, RT2103: NTC 10k lug probe (CUSTOM)

Connections:
AGND: C2101.2, C2102.2, C2103.2, C2104.2, C2105.2, C2106.2, J2101.2, J2102.2, J2103.2, J2104.2, J2105.2, J2106.2, RT2101.2 (T2), RT2102.2 (T2), RT2103.2 (T2)
NTC1: C2101.1, J2101.1, RT2101.1 (T1)
NTC2: C2103.1, J2103.1, RT2102.1 (T1)
NTC3: C2105.1, J2105.1, RT2103.1 (T1)
NTC5: C2102.1, J2102.1
NTC6: C2104.1, J2104.1
NTC7: C2106.1, J2106.1
PE: HS2101.1, HS2102.1, HS2103.1, MH2101.1, RT2101.3 (LUG), RT2102.3 (LUG), RT2103.3 (LUG)

Notes on the sheet:
PE AND HEATSINK
NTC1-3 = heatsink sections a-c: lug probe on the EARTHED heatsink, >= 2.5 kV rms lead-to-lug (R-10). NTC5-7 = L1 winding NTCs (leads on 2-pin headers). 100 nF at each header.
Three earthed heatsink sections (one per leg); the Al2O3 pads isolate the device tabs (basic DC-PE).
NTC INPUTS (NTC TO AGND, BIASED ON THE CONTROL BOARD)
