vectivolt/PCM/hardware/PCS-PWR/sheets/22_supplies.kicad_sch

## KiCad design hardware/PCS-PWR/sheets/22_supplies.kicad_sch (2026-10-06)

Schematic: 22_supplies.kicad_sch

Parts:
C2201, C2202, C2208, C2209: 4.7u 50V
C2203, C2210: 100n 100V
C2204, C2211, C2215, C2218: 100n 50V
C2205, C2206, C2207, C2212, C2213, C2214: 22u 16V
C2216: 1n 50V
C2217: 10u 25V
C2219: 470p 50V
C2220, C2221: 22u 10V
D2201: BZX84-B10; MPN BZX84-B10
J2201: KF2EDGR-3.5-2P; MPN KF2EDGR-3.5-2P
L2201, L2202: 74437368150; MPN 74437368150
L2203: 74438356022; MPN 74438356022
Q2201: PMV30ENEAR; MPN PMV30ENEAR
Q2202: 2N7002BK; MPN 2N7002BK
R2201, R2205: 64.9k
R2202, R2204, R2206, R2208, R2214: 100k
R2203, R2207: 24.9k
R2209: 107k
R2210, R2212: 10k
R2211: 31.6k
R2213: 1.2R
TP2201, TP2202: TP
U2201, U2202: LMR38020FDDAR; MPN LMR38020FDDAR
U2203: TPS3710DDCR; MPN TPS3710DDCR
U2204: TPS62130RGTR; MPN TPS62130RGTR

Connections:
+3V3: C2220.1, C2221.1, L2203.2, R2211.1, R2213.1, U2204.14 (VOS)
+5V: C2205.1, C2206.1, C2207.1, L2201.2, R2202.1, R2204.1
+5V_GD: C2212.1, C2213.1, C2214.1, C2215.1, C2217.1, C2218.1, L2202.2, R2206.1, R2208.1, R2209.1, U2203.5 (VDD), U2204.10 (AVIN), U2204.11 (PVIN), U2204.12 (PVIN)
+24V: C2201.1, C2202.1, C2203.1, C2208.1, C2209.1, C2210.1, R2214.1, U2201.2 (EN), U2201.3 (VIN), U2202.2 (EN), U2202.3 (VIN)
BOOT_5V: C2204.1, U2201.7 (BOOT)
BOOT_5VG: C2211.1, U2202.7 (BOOT)
DIS_D: Q2201.3 (D), R2213.2
DIS_G: D2201.3 (K), Q2201.1 (G), Q2202.3 (D), R2214.2
FB_3V3: R2211.2, R2212.1, U2204.5 (FB)
FB_5V: R2202.2, R2203.1, U2201.5 (FB)
FB_5VG: R2206.2, R2207.1, U2202.5 (FB)
GND: C2201.2, C2202.2, C2203.2, C2205.2, C2206.2, C2207.2, C2208.2, C2209.2, C2210.2, C2212.2, C2213.2, C2214.2, C2215.2, C2216.2, C2217.2, C2218.2, C2219.2, C2220.2, C2221.2, D2201.1 (A), Q2201.2 (S), Q2202.2 (S), R2201.2, R2203.2, R2205.2, R2207.2, R2210.2, R2212.2, U2201.1 (GND), U2201.9 (EP), U2202.1 (GND), U2202.9 (EP), U2203.2 (GND), U2203.4 (GND), U2203.6 (GND), U2204.6 (AGND), U2204.7 (FSW), U2204.8 (DEF), U2204.15 (PGND), U2204.16 (PGND), U2204.17 (EP)
PG_5V: R2204.2, TP2201.1, U2201.6 (PG)
PG_5VG: Q2202.1 (G), R2208.2, TP2202.1, U2202.6 (PG), U2204.13 (EN)
RDY: U2203.1 (OUT)
RT_5V: R2201.1, U2201.4 (RT/SYNC)
RT_5VG: R2205.1, U2202.4 (RT/SYNC)
SELV_0V: J2201.2
SELV_24V: J2201.1
SS_3V3: C2219.1, U2204.9 (SS/TR)
SUP5G_SNS: C2216.1, R2209.2, R2210.1, U2203.3 (SENSE)
SW_3V3: L2203.1, U2204.1 (SW), U2204.2 (SW), U2204.3 (SW)
SW_5V: C2204.2, L2201.1, U2201.8 (SW)
SW_5VG: C2211.2, L2202.1, U2202.8 (SW)

Notes on the sheet:
+3V3 DISCHARGE (RAMP-DOWN WHEN THE RAILS FAIL)
gate bias of legs b and c, +3V3 (TPS62130). ctrl_c2000 circuit (SNVSC40E table 9-1, 400 kHz / 5 V / 2 A): 15 uH, 3 x 22 uF, RT 64.9k, FB 100k / 24.9k 0.1 % -> 4.93-5.10 V. Load in design_check (<= 80 % of 2 A).
TPS3710 107k/10k as on +5V: RDY low while the bias rail of phases 3 is below 4.52-4.69 V.
AUX-T1 reinforced winding SELV_24V / SELV_0V, cross-regulated 21.4-30.1 V (aux75_spec); full fan speed needs 24.5 V. Full fan speed is only guaranteed while the converter is switching. Fan buck (12-36 V in) + SELV logic on the control board; >= 10 mm from live copper; nothing else of the SELV domai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
24 V -> +5V_GD (LMR38020, 400 KHZ, 2 A)
EN = PG_5VG. FB 31.6k / 10k 0.1 % -> 3.240-3.433 V (>= 3.20 V for the control board's reference). SS/TR 470p C0G: ramp-up 12-16 mV/us (F28003x VDDIO 8-100 mV/us). Ports' logic, RDY / MOV_OK pull-ups, PC +3V3 (control <= 157 mA).
24 V -> +5V (LMR38020, 400 KHZ, 2 A)
+5V_GD -> +3V3 (TPS62130, 2.5 MHZ) WITH A CONTROLLED RAMP
PG_5VG low (+5V_GD < 90-94 %, i.e. the live 24 V is gone) disables the TPS62130 and lets the 100k from +24V (10 V Zener) turn on PMV30ENEA + 1.2R: +3V3 falls at >= 20 mV/us through the BOR region (F28003x SRVDDIO-DN).
NSI6651 inputs, AHCT, sensors, references, PC +5V, gate bias of phases 1-2. ctrl_c2000 circuit (SNVSC40E table 9-1, 400 kHz / 5 V / 2 A): 15 uH, 3 x 22 uF, RT 64.9k, FB 100k / 24.9k 0.1 % -> 4.93-5.10 V. Load in design_check (<= 80 % of 2 A).
SELV 24 V TO THE CONTROL BOARD (J2)
+5V_GD SUPERVISOR ON RDY
