vectivolt/PCM/hardware/PCS-PWR/sheets/23_aux75_input.kicad_sch

## KiCad design hardware/PCS-PWR/sheets/23_aux75_input.kicad_sch (2026-10-06)

Schematic: 23_aux75_input.kicad_sch

Parts:
C2301, C2302: 3.3u 1300V; MPN FCSA3DS335K050ID90BE3
D2301, D2302: BYG10Y-E3/TR; MPN BYG10Y-E3/TR
F2301, F2302: 0090.1001; MPN 0090.1001
R2301, R2302, R2303, R2304: 20R; MPN AC10000002009JAB00

Connections:
AUX_HV_BULK: C2301.1, C2302.1, D2301.1 (K), D2302.1 (K)
AUX_PA_F: D2301.2 (A), F2301.2
AUX_PA_R1: R2301.2, R2302.1
AUX_PA_RF: F2301.1, R2302.2
AUX_PB_F: D2302.2 (A), F2302.2
AUX_PB_R1: R2303.2, R2304.1
AUX_PB_RF: F2302.1, R2304.2
B_T+: R2301.1
DC+: R2303.1
DC-: C2301.2, C2302.2

Notes on the sheet:
2 per tap AHEAD of the fuse (AC10 pulse-rated, 20 R = the smallest E24 value inside AX-01 / 02: hot-plug I2t 18.1 % of the fuse melting I2t (rule 20 %), film surge 1218 V); 4.64 W each at the highest input current (0.48 A, 250 V) Fuse: (30 W case, unchanged) per-port fuse 1000 VDC gPV behind 44R: f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
TAP DC+
Film: (30 W case, unchanged) 2 x film = RC surge absorber with 44R: 4 kV / 20 us residual -> 1199 V (UR 1300 V); filter corner 546 Hz.
TAP B_T+
SURGE ABSORBER / INPUT FILTER
