vectivolt/PCM/hardware/PCS-PWR/sheets/24_aux75_startup.kicad_sch

## KiCad design hardware/PCS-PWR/sheets/24_aux75_startup.kicad_sch (2026-10-06)

Schematic: 24_aux75_startup.kicad_sch

Parts:
C2401, C2402, C2403: 100p 1kV
C2404: 68n 50V
C2405: 12n 50V
C2406, C2407: 100n 50V
C2408: 220p 50V
C2409: 680n 25V
D2401, D2402: BAT54,215; MPN BAT54,215
D2403: BAS16,215; MPN BAS16,215
Q2401, Q2402, Q2403: BSS126H6327XTSA2; MPN BSS126H6327XTSA2
Q2404, Q2405: 2N7002BK,215; MPN 2N7002BK,215
R2401, R2402, R2403: 10M; MPN CRHV2512AF10M0FKFB
R2404: 8.45k
R2405: 57.6k
R2406, R2412: 4.7k
R2407, R2415: 1M
R2408, R2414: 10k
R2409, R2417, R2419: 100k
R2410: 47k
R2411: 6.81M
R2413, R2418: 1k
R2416: 73.2k
U2401: TPS3710DDCR; MPN TPS3710DDCR
U2402: ATL431BIDBZR; MPN ATL431BIDBZR
U2403: TLV3202AIDGKR; MPN TLV3202AIDGKR

Connections:
AUX_COMP: D2401.1 (A), D2402.1 (A), R2416.1
AUX_COMPF: C2409.1, D2403.3 (K), R2416.2, R2417.1, U2403.5 (2IN+)
AUX_HV_BULK: C2401.1, Q2401.3 (D), R2401.1
AUX_LINE_OK: D2401.3 (K), R2410.2, R2411.1, U2401.1 (OUT)
AUX_LS: C2404.2, C2405.1, R2404.2, R2405.1, R2411.2, U2401.3 (SENSE)
AUX_LSO: C2403.2, C2404.1, R2403.2, R2404.1, R2413.1
AUX_LSOF: C2408.1, R2413.2, U2403.2 (1IN-)
AUX_OLATCH: D2403.1 (A), R2418.1, U2403.7 (2OUT)
AUX_OVL_N: D2402.3 (K), R2415.1, U2403.1 (1OUT)
AUX_OVREF: R2414.2, R2415.2, U2403.3 (1IN+)
AUX_SS: Q2405.3 (D)
AUX_SSG: Q2405.1 (G), R2418.2, R2419.1
AUX_SU_EN: Q2404.1 (G), R2408.2, R2409.1
AUX_SU_G: Q2403.1 (G), Q2404.3 (D), R2407.1
AUX_SU_RS: Q2403.2 (S), R2406.1
AUX_SU_S1: Q2402.2 (S), Q2403.3 (D)
AUX_SU_S2: Q2401.2 (S), Q2402.3 (D)
AUX_SU_T1: C2402.2, C2403.1, Q2402.1 (G), R2402.2, R2403.1
AUX_SU_T2: C2401.2, C2402.1, Q2401.1 (G), R2401.2, R2402.1
AUX_VDD: R2406.2, R2407.2
AUX_VR25: R2412.2, R2414.1, U2402.1 (K), U2402.2 (REF), U2403.6 (2IN-)
AUX_VREF: C2406.1, C2407.1, R2408.1, R2410.1, R2412.1, U2401.5 (VDD), U2403.8 (VCC)
DC-: C2405.2, C2406.2, C2407.2, C2408.2, C2409.2, Q2404.2 (S), Q2405.2 (S), R2405.2, R2409.2, R2417.2, R2419.2, U2401.2 (GND), U2401.4 (GND), U2401.6 (GND), U2402.3 (A), U2403.4 (GND)

Notes on the sheet:
LINE_OK low -> BAT54 holds COMP below the 1.15 V offset.
DEPLETION CASCODE CURRENT SOURCE
INPUT OV LOCKOUT AND OVERLOAD TIMER
Ch 1: OV lockout -> COMP low. Ch 2: timer divider: trips above 113 / 175 / 278 W (no trip at the 112.2 W 1 s peak); timer 39-100 ms -> latch -> SS crowbar -> hiccup.
VREF high -> start-up off (as AUX-HV).
COMPENSATED TAP STRING
string tap, brown-in 206-215 V, brown-out 179-192 V brown-in hysteresis (same solve); OV lockout 1107-1162 V
LINE BROWN-IN
