vectivolt/PCM/hardware/PCS-PWR/sheets/25_aux75_power.kicad_sch

## KiCad design hardware/PCS-PWR/sheets/25_aux75_power.kicad_sch (2026-10-06)

Schematic: 25_aux75_power.kicad_sch

Parts:
C2501: 1u 25V
C2502: 1n 50V
C2503, C2504, C2505, C2506, C2507, C2508, C2509, C2510: 10u 50V
C2511: 100n 50V
C2512: 3.3n 50V
C2513: 120p 50V
C2514: 2.2u 16V
C2515: 470p 50V
C2516: 10n 50V
C2517: 150p 50V
C2518, C2519: 22n 2kV
D2501: BZX84-B20,215; MPN BZX84-B20,215
D2502: BAT54S,215; MPN BAT54S,215
D2503: BZX84-A18,215; MPN BZX84-A18,215
D2504: BAT54,215; MPN BAT54,215
D2505: US1G-13-F; MPN US1G-13-F
D2506: BZX84-B6V8,215; MPN BZX84-B6V8,215
D2507: BYG10Y-E3/TR; MPN BYG10Y-E3/TR
D2508, D2509, D2510, D2511, D2512, D2513: SMCJ33A; MPN SMCJ33A
Q2501: BC817-25,215; MPN BC817-25,215
Q2502, Q2503: 2N7002BK,215; MPN 2N7002BK,215
Q2504: IV2Q171R0D7Z; MPN IV2Q171R0D7Z
R2501: 13.7k
R2502: 86.6k
R2503, R2506, R2507, R2513: 10k
R2504: 348k
R2505: 100k
R2508: 4.7k
R2509: 22k
R2510: 1M
R2511: 47k
R2512: 10R
R2514, R2515, R2516: 0.866R
R2517: 1k
R2518: 10M; MPN CRHV2512AF10M0FKFB
T2501: AUX-T1 75 W (CUSTOM); MPN AUX-T1 75 W (CUSTOM)
U2501: UCC28C59QDRQ1; MPN UCC28C59QDRQ1

Connections:
+24V: Q2501.3 (C), R2502.1, R2506.1
AUX_AF1: C2515.1, D2506.3 (K), R2508.2, R2509.1
AUX_AFR: D2505.1 (K), R2508.1
AUX_CLMP: D2507.1 (K), D2508.1 (K)
AUX_COMP: C2513.1, D2502.1 (A), R2504.1, U2501.1 (COMP)
AUX_CS: C2517.1, R2517.2, R2518.2, U2501.3 (CS)
AUX_CTXD: C2516.2, Q2503.3 (D)
AUX_DRAIN: D2507.2 (A), Q2504.8 (D), T2501.1 (PS)
AUX_EA_M: C2512.1, R2504.2
AUX_FB: C2512.2, C2513.2, R2502.2, R2503.1, U2501.2 (FB)
AUX_FBK: Q2502.3 (D), Q2503.1 (G), R2511.2
AUX_GATE: Q2504.1 (G), R2512.2, R2513.1
AUX_HV_BULK: C2518.1, C2519.1, D2513.2 (A), R2518.1, T2501.2 (PF)
AUX_LIVE_A: D2505.2 (A), T2501.4 (LS)
AUX_OUT: R2512.1, U2501.6 (OUT)
AUX_QIG: D2506.1 (A), Q2502.1 (G), R2510.1
AUX_RTCT: C2502.1, C2516.1, R2501.2, U2501.4 (RT/CT)
AUX_SELV_A: T2501.9 (SS)
AUX_SRC: Q2504.2 (KS), Q2504.3 (S), Q2504.4 (S), Q2504.5 (S), Q2504.6 (S), Q2504.7 (S), R2513.2, R2514.1, R2515.1, R2516.1, R2517.1
AUX_SS: C2514.1, D2502.3 (COM), R2505.2
AUX_TVM1: D2508.2 (A), D2509.1 (K)
AUX_TVM2: D2509.2 (A), D2510.1 (K)
AUX_TVM3: D2510.2 (A), D2511.1 (K)
AUX_TVM4: D2511.2 (A), D2512.1 (K)
AUX_TVM5: D2512.2 (A), D2513.1 (K)
AUX_VDD: C2503.1, C2504.1, C2505.1, C2506.1, C2507.1, C2508.1, C2509.1, C2510.1, C2511.1, D2501.3 (K), D2504.3 (K), U2501.7 (VDD)
AUX_VDD_E: D2504.1 (A), Q2501.2 (E), R2507.1
AUX_VREF: C2501.1, D2502.2 (K), R2501.1, R2505.1, R2511.1, U2501.8 (VREF)
AUX_ZB: D2503.3 (K), Q2501.1 (B), R2506.2
DC-: C2501.2, C2502.2, C2503.2, C2504.2, C2505.2, C2506.2, C2507.2, C2508.2, C2509.2, C2510.2, C2511.2, C2514.2, C2515.2, C2517.2, C2518.2, C2519.2, D2501.1 (A), D2503.1 (A), Q2502.2 (S), Q2503.2 (S), R2503.2, R2507.2, R2509.2, R2510.2, R2514.2, R2515.2, R2516.2, T2501.3 (SH), T2501.5 (LF), U2501.5 (GND)
SELV_0V: T2501.8 (SF)

Notes on the sheet:
3 in parallel = 0.288667R (E96): lowest limit 3.04 A delivers 112.8 W (>= the 112.2 W 1 s peak) at every input; highest 4.07 A with the line feed-forward (4.46 A without) line feed-forward HV_BULK -> CS (CRHV2512): CS offset 101 mV at 1000 V cancels most of the 155-250 ns CS-delay overshoot, so the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
VDD FOLLOWER FROM THE LIVE 24 V
AUX-T1 (CUSTOM - THE MODULE'S REINFORCED SUPPLY BARRIER B1)
PWM CONTROLLER AND ERROR AMPLIFIER
Lp 0.485 mH +/-7 %; shield and live winding on DC-; SELV winding reinforced (PD <= 10 pC routine test). Electrical requirement: aux75_spec.json transformer_requirement.
live 24 V into FB: 23.62 / 24.15 / 24.68 V (VFB 2.45-2.55 V, 0.1 %) type II: mid-band gain 4.0; crossover 259-727 Hz, phase margin >= 60 deg type II zero 139 Hz type II pole 3811 Hz
SIC SWITCH, CURRENT SENSE, LINE FEED-FORWARD, CLAMP
(30 W case, unchanged) follower Zener bias: VDD = gate drive 15.46-18.11 V (BZX84-A18, -40..85 C)
(30 W case, unchanged) foldback: switched onto RT/CT below 7.7-10.1 V output -> fsw 5.9 kHz (5.3-6.8)
FREQUENCY FOLDBACK ON THE LIVE WINDING PLATEAU (AX-03)
