vectivolt/PCM/hardware/PCS-PWR/sheets/26_aux75_outputs.kicad_sch

## KiCad design hardware/PCS-PWR/sheets/26_aux75_outputs.kicad_sch (2026-10-06)

Schematic: 26_aux75_outputs.kicad_sch

Parts:
C2601, C2607: 68p 500V
C2602, C2603: 35ZLH1500MEFC12.5X30; MPN 35ZLH1500MEFC12.5X30
C2604, C2608, C2609, C2610: PCV1HVF101MB12FV-WE3; MPN PCV1HVF101MB12FV-WE3
C2605, C2606, C2611, C2612: 10u 50V
C2613: 100n 16V
C2614: 1n 50V
D2601, D2602: VS-8ETU04S-M3; MPN VS-8ETU04S-M3
D2603: BZX84-B3V3,215; MPN BZX84-B3V3,215
D2604: BAT54,215; MPN BAT54,215
R2601, R2602: 150R
R2603, R2606: 10k
R2604: 649k
R2605: 2.15k
R2607: 100k
U2601: TPS3700DDCR; MPN TPS3700DDCR

Connections:
+24V: C2601.2, C2602.1, C2603.1, C2604.1, C2605.1, C2606.1, D2601.2 (K), R2603.1, R2604.1
AUX_LIVE_A: D2601.3 (A), R2601.1
AUX_PG3V3: C2613.1, D2603.3 (K), R2603.2, U2601.5 (VDD)
AUX_PG_OV: R2605.2, R2606.1, U2601.4 (INB-)
AUX_PG_OVN: D2604.3 (K), R2607.2, U2601.6 (OUTB)
AUX_PG_UV: C2614.1, R2604.2, R2605.1, U2601.3 (INA+)
AUX_SELV_A: D2602.3 (A), R2602.1
AUX_SN_L: C2601.1, R2601.2
AUX_SN_S: C2607.1, R2602.2
AUX_SS: D2604.1 (A)
AUX_VREF: R2607.1
DC-: C2602.2, C2603.2, C2604.2, C2605.2, C2606.2, C2613.2, C2614.2, D2603.1 (A), R2606.2, U2601.2 (GND)
RDY: U2601.1 (OUTA)
SELV_0V: C2608.2, C2609.2, C2610.2, C2611.2, C2612.2
SELV_24V: C2607.2, C2608.1, C2609.1, C2610.1, C2611.1, C2612.1, D2602.2 (K)

Notes on the sheet:
STATUS AND OUTPUT OV STOP (TPS3700 ON A 3.3 V ZENER RAIL)
LIVE 24 V RECTIFIER, HOLD-UP
D2PAK tab = cathode on the output. Snubber 150R + 68p.
SELV 24 V RECTIFIER (REINFORCED SIDE)
TPS3700 window on the live 24 V: UV falls 21.02-21.81 V (status), OV rises 26.13-26.76 V (SS pulled low)
Cross-regulated from the live winding.
