vectivolt/PCM/hardware/PCS-PWR/sheets/27_acstart.kicad_sch

## KiCad design hardware/PCS-PWR/sheets/27_acstart.kicad_sch (2026-10-06)

Schematic: 27_acstart.kicad_sch

Parts:
D2701, D2702, D2703, D2704, D2705, D2706, D2707: BYG10Y-E3/TR; MPN BYG10Y-E3/TR
D2708: SMBJ33A; MPN SMBJ33A
D2709: S2M-13-F; MPN S2M-13-F
F2701, F2702, F2703: 1.6A 500VAC; MPN ABB-A 1.60
K2701: G7L-2A-X DC24; MPN G7L-2A-X DC24
Q2701: BSS138BK; MPN BSS138BK
Q2702: IRFR9214TRPbF; MPN IRFR9214TRPbF
R2701, R2702, R2703: 20R; MPN AC10000002009JAB00
R2704: 220R RFQ
R2705: 100k
R2706, R2707: 10k

Connections:
+24V: Q2702.3 (S), R2707.1
ACPRE_COIL: D2708.2 (A), K2701.1 (COIL), Q2702.2 (D)
ACPRE_M: K2701.4 (P2), K2701.6 (P1)
ACPRE_R: K2701.2 (P2-), R2704.1
ACP_K_PD: Q2701.3 (D), R2706.1
ACP_K_PG: Q2702.1 (G), R2706.2, R2707.2
ACP_K_Z: D2708.1 (K), D2709.1 (K)
ACT_A: D2701.2 (A), D2702.1 (K), F2701.2
ACT_A_R: F2701.1, R2701.2
ACT_B: D2703.2 (A), D2704.1 (K), F2702.2
ACT_B_R: F2702.1, R2702.2
ACT_C: D2705.2 (A), D2706.1 (K), F2703.2
ACT_C_R: F2703.1, R2703.2
ACT_P: D2701.1 (K), D2703.1 (K), D2705.1 (K), D2707.2 (A), K2701.8 (P1+)
AUX_HV_BULK: D2707.1 (K)
DC+: R2704.2
DC-: D2702.2 (A), D2704.2 (A), D2706.2 (A)
GND: D2709.2 (A), K2701.0 (COIL), Q2701.2 (S), R2705.2
K2O_A: R2701.1
K2O_B: R2702.1
K2O_C: R2703.1
K_ACPRE: Q2701.1 (G), R2705.1

Notes on the sheet:
OR INTO THE AUX INPUT (75 W BLOCK'S AUX_HV_BULK)
K_ACPRE = PCS_PC PWM16, gated by the trip latch on the control board; logic lost = coil off.
The tap's + rail feeds the aux through its own BYG10Y: the aux runs from the grid with the DC side dead (565-650 V rectified at 400-460 V AC, inside its 250 V..1000 V full-power range).
GRID TAP (LIVE DOMAIN: THE LOWER DIODES TIE DC- TO THE GRID PHASES; BASIC OVC III TO PE AS THE AC SIDE)
COIL DRIVER (PORT._LEAN_DRV) FROM K_ACPRE
Per phase from K2O_x (grid side of K1 / K2, works with the contactors open; behind the CM choke and the AC SPD): AC10 20 ohm (inrush, surge and fault limit ahead of the fuse) -> ABB-A 1.60 (1.6 A, 500 V AC, 200 A interrupting) -> bridge.
AC PRECHARGE: G7L-2A-X (DC, POLES IN SERIES, NORMAL POLARITY) + 220 OHM RPRE_AL FROM ACT_P TO DC+
Charges the DC link to the line-to-line peak through the tap with the main contactors open (pcs_spec ac_start); firmware interlocks: K_ACPRE only with K_B, K_PRE, K_A, K_AC2 open; abort / retry / welded-relay rules.
