vectivolt/PCM/hardware/PORT-LEAN-HOLD/sheets/01_lean_io.kicad_sch

## KiCad design hardware/PORT-LEAN-HOLD/sheets/01_lean_io.kicad_sch (2026-10-04)

Schematic: 01_lean_io.kicad_sch

Parts:
J101: PORT-LEAN verification: supplies and controller l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
J102: PORT-LEAN verification: port terminals and banks
LK101: PE_T link to chassis PE: removable strap, OPEN fo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
MH101: PE bond M4 (IMD divider reference)
R101, R102: 0R

Connections:
+3V3: J101.3
+5V: J101.2
+24V: J101.1
AGND: R101.1
A_BK+: J102.5
A_IM: J101.12
A_IN+: J102.1
A_IN-: J102.2
BUS-: J102.7, R102.2
B_BK+: J102.6
B_IM: J101.13
B_IN+: J102.3
B_IN-: J102.4
CMD_IMDN: J101.9
CMD_IMDP: J101.8
CMD_KA: J101.5
CMD_KB: J101.6
CMD_PB: J101.7
GND: J101.4, R101.2, R102.1
IMD_AUX_O: J101.14
PE: LK101.2 (PE)
PE_D: MH101.1
PE_T: LK101.1 (PE_T)

Notes on the sheet:
SUPPLIES AND COMMANDS
On the power board these come from the AUX-T1 live winding and the controller.
