vectivolt/PCM/hardware/PORT-LEAN-HOLD/sheets/02_leanA_power.kicad_sch

## KiCad design hardware/PORT-LEAN-HOLD/sheets/02_leanA_power.kicad_sch (2026-10-05)

Schematic: 02_leanA_power.kicad_sch

Parts:
C301, C302, C305, C306, C307, C310, C311, C402, C403: 100n 50V
C303: 470p 50V
C304: 1n 50V
C308, C309: 4.7n 50V
C401: 1u 50V
D201: BAS16; MPN BAS16
D401: BZX84-C15; MPN BZX84-C15
D402: SMBJ33A; MPN SMBJ33A
D403: S2M-13-F; MPN S2M-13-F
F201, F202: 36A gPV 14x51; MPN 002637115
K401: HFE82V-300C/1000-24-H-C5-1; MPN HFE82V-300C/1000-24-H-C5-1
Q401: PMV30ENEAR; MPN PMV30ENEAR
Q402: BSS138BK; MPN BSS138BK
Q403: IRFR9214TRPbF; MPN IRFR9214TRPbF
R201, R202, R203, R204, R205, R206, R207, R208, R209, R210, R211, R212: 82.5k
R213: 220k
R301: 11.8k
R302, R303: 1.65k
R304: 14.7k
R305: 3.57k
R306, R308: 6.04k
R307: 8.06k
R309: 6.49k
R310, R312, R314, R316: 1.00k
R311, R313: 30.1k
R315, R317: 10.0k
R318, R319, R320, R321, R322, R323, R325, R326, R327, R328, R329, R330: 1M; MPN ARHV06BTC1004A
R324, R331: 4.99k; MPN TNPW12064K99BEEA
R401, R402, R403, R404: 37.4
R405: 56k
R406, R407: 100k
R408, R409: 10k
R410, R411, R412, R413, R414, R415, R416, R417: 73.2k
RS301, RS302: 0.2m; MPN CSS2H-3920R-L200F
RV201, RV202, RV203: TVT25751KFKG; MPN TVT25751KFKG
U201: CNY65B; MPN CNY65B
U301: REF3030EAIDBZR; MPN REF3030EAIDBZR
U302, U305, U306: OPA2388IDR; MPN OPA2388IDR
U303: TLV3502AIDCNR; MPN TLV3502AIDCNR
U304, U402: SN74LVC1G32DBVR; MPN SN74LVC1G32DBVR
U401: SN74LVC1G11DBVR; MPN SN74LVC1G11DBVR
X201, X202, X203, X204: 006710340; MPN 006710340

Connections:
+3V3: C305.1, C306.1, C307.1, C310.1, C311.1, C402.1, C403.1, R213.1, U302.8 (V+), U303.8 (V+), U304.5 (VCC), U305.8 (V+), U306.8 (V+), U401.5 (VCC), U401.6 (C), U402.5 (VCC)
+5V: C301.1, U301.1 (IN)
+24V: Q403.3 (S), R409.1
AGND: C301.2, C302.2, C305.2, C306.2, C307.2, C310.2, C311.2, C402.2, C403.2, R304.2, R309.2, U201.3 (E), U301.3 (GND), U302.4 (V-), U303.5 (V-), U304.3 (GND), U305.4 (V-), U306.3 (+INA), U306.4 (V-), U401.2 (GND), U402.3 (GND)
A_BK+: K401.A2, R325.1, R410.1
A_BL1: R410.2, R411.1
A_BL2: R411.2, R412.1
A_BL3: R412.2, R413.1
A_BL4: R413.2, R414.1
A_BL5: R414.2, R415.1
A_BL6: R415.2, R416.1
A_BL7: R416.2, R417.1
A_HOLD: U304.4 (Y), U401.1 (A)
A_HOLDN: U303.6 (OUTB), U304.2 (B)
A_HOLDP: U303.7 (OUTA), U304.1 (A)
A_HOLD_HI: R305.2, R306.1, U303.2 (-INA)
A_HOLD_LO: R308.2, R309.1, U303.3 (+INB)
A_IH: C304.2, R317.2, U302.7 (OUTB), U303.1 (+INA), U303.4 (-INB)
A_IM: C303.2, R313.2, U302.1 (OUTA)
A_IN+: F201.1, K401.A1, R318.1, X201.1
A_IN-: F202.1, R310.1, R314.1, RS301.1, RS302.1, X203.1
A_K_COIL: C401.1, D402.2 (A), K401.1 (COIL1), Q403.2 (D)
A_K_G: Q402.1 (G), R407.1, U401.3 (B), U402.4 (Y)
A_K_GB: C401.2, D401.3 (K), Q401.1 (G), R405.1
A_K_H1: R401.2, R402.1
A_K_H2: R402.2, R403.1
A_K_H3: R403.2, R404.1
A_K_HG: U401.4 (Y), U402.2 (B)
A_K_LO: K401.2 (COIL2), Q401.3 (D), R401.1
A_K_PD: Q402.3 (D), R408.1
A_K_PG: Q403.1 (G), R408.2, R409.2
A_K_Z: D402.1 (K), D403.1 (K)
A_MON1: R201.1, RV201.3 (MON)
A_MON2: R212.2, RV202.3 (MON)
A_MON3: D201.1 (A), RV203.3 (MON), U201.2 (K)
A_MONA: D201.3 (K), R206.2, U201.1 (A)
A_MR1: R201.2, R202.1
A_MR2: R202.2, R203.1
A_MR3: R203.2, R204.1
A_MR4: R204.2, R205.1
A_MR5: R205.2, R206.1
A_MS1: R207.2, R208.1
A_MS2: R208.2, R209.1
A_MS3: R209.2, R210.1
A_MS4: R210.2, R211.1
A_MS5: R211.2, R212.1
A_OC_HI: R306.2, R307.1
A_OC_LO: R307.2, R308.1
A_REF: C302.1, R301.1, R305.1, U301.2 (OUT)
A_SHAN: C303.1, R312.2, R313.1, U302.2 (-INA)
A_SHAP: R310.2, R311.1, U302.3 (+INA)
A_SHBN: C304.1, R316.2, R317.1, U302.6 (-INB)
A_SHBP: R314.2, R315.1, U302.5 (+INB)
A_SP+: F201.2, RV201.1 (L), X202.1
A_SP-: F202.2, RV202.1 (L), X204.1
A_SPARE: U306.1 (OUTA), U306.2 (-INA)
A_SPD_N: R213.2, U201.4 (C)
A_SPM: R207.1, RV201.2 (N), RV202.2 (N), RV203.1 (L)
A_TH_HI: R301.2, R302.1
A_TH_LO: R303.2, R304.1
A_VBD: C309.1, R330.2, R331.1, U305.5 (+INB)
A_VBD_1: R325.2, R326.1
A_VBD_2: R326.2, R327.1
A_VBD_3: R327.2, R328.1
A_VBD_4: R328.2, R329.1
A_VBD_5: R329.2, R330.1
A_VB_O: U305.6 (-INB), U305.7 (OUTB)
A_VMID: C308.2, C309.2, R311.2, R315.2, R324.2, R331.2, U306.6 (-INB), U306.7 (OUTB)
A_VMIDR: R302.2, R303.1, U306.5 (+INB)
A_VXD: C308.1, R323.2, R324.1, U305.3 (+INA)
A_VXD_1: R318.2, R319.1
A_VXD_2: R319.2, R320.1
A_VXD_3: R320.2, R321.1
A_VXD_4: R321.2, R322.1
A_VXD_5: R322.2, R323.1
A_VX_O: U305.1 (OUTA), U305.2 (-INA)
BUS-: R312.1, R316.1, R417.2, RS301.2, RS302.2
CMD_KA: R406.1, U402.1 (A)
GND: D401.1 (A), D403.2 (A), Q401.2 (S), Q402.2 (S), R404.2, R405.2, R406.2, R407.2
PE_T: RV203.2 (N)

Notes on the sheet:
ON-BOARD SURGE PROTECTION: VARISTOR Y (IC-01, IC-12)
PORT A (PV SOURCE), D-044 LEAN PORT
TVT25751 x 3 (615 VDC, thermal link + monitor lead): MOV1 +/M, MOV2 -/M, MOV3 M/PE_T. Up,eff 3793 V pole-PE and pole-pole at In 3 kA (calc., <= 4.0 kV -> reinforced 6 kV / basic 4 kV, D-032); Imax 25 kA. Branch fuses ETI CH14x51 gPV 36 A 30 kA (L/R 2 ms). Monitor loop through both fuses and all thr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
Terminal side A_IN+ / A_IN-, bank A_BK+. No fuse, no precharge: array Isc <= 1.25 x rating. Contactor opens <= 0.97 kA, held above (port_spec lean). Installation: upstream clears 967-1250 A within 0.26 s.
