vectivolt/PCM/hardware/PORT-LEAN-HOLD/sheets/05_leanB_power.kicad_sch

## KiCad design hardware/PORT-LEAN-HOLD/sheets/05_leanB_power.kicad_sch (2026-10-05)

Schematic: 05_leanB_power.kicad_sch

Parts:
C601: 470p 50V
C602: 1n 50V
C603, C604, C605, C608, C609, C702, C703, C802: 100n 50V
C606, C607, C801: 4.7n 50V
C701: 1u 50V
D501: BAS16; MPN BAS16
D701: BZX84-C15; MPN BZX84-C15
D702, D704: SMBJ33A; MPN SMBJ33A
D703, D705: S2M-13-F; MPN S2M-13-F
F501, F502: 36A gPV 14x51; MPN 002637115
F503, F504: HPE501/000B100-250; MPN HPE501/000B100-250
K701: HFE82V-300C/1000-24-H-C5-1; MPN HFE82V-300C/1000-24-H-C5-1
K702: G7L-2A-X DC24; MPN G7L-2A-X DC24
Q701: PMV30ENEAR; MPN PMV30ENEAR
Q702, Q704, Q801, Q802: BSS138BK; MPN BSS138BK
Q703, Q705: IRFR9214TRPbF; MPN IRFR9214TRPbF
R501, R502, R503, R504, R505, R506, R507, R508, R509, R510, R511, R512: 82.5k
R513: 220k
R601, R603, R605, R607: 1.00k
R602, R604: 30.1k
R606, R608: 10.0k
R609, R610, R611, R612, R613, R614, R616, R617, R618, R619, R620, R621, R801, R802, R803, R804, R805, R806: 1M; MPN ARHV06BTC1004A
R615, R622, R807: 4.99k; MPN TNPW12064K99BEEA
R701, R702, R703, R704: 37.4
R705: 56k
R706, R707, R719, R817, R827: 100k
R708, R709, R720, R721: 10k
R710, R711, R712, R713, R714, R715, R716, R717: 73.2k
R718: 220R RFQ
R808, R809, R810, R811, R812, R813, R814, R815, R818, R819, R820, R821, R822, R823, R824, R825: 124k; MPN ARHV13BTC1243A
R816, R826: 330R
RS601, RS602: 0.2m; MPN CSS2H-3920R-L200F
RV501, RV502, RV503: TVT25751KFKG; MPN TVT25751KFKG
U501: CNY65B; MPN CNY65B
U601, U604, U605, U801: OPA2388IDR; MPN OPA2388IDR
U602: TLV3502AIDCNR; MPN TLV3502AIDCNR
U603, U702: SN74LVC1G32DBVR; MPN SN74LVC1G32DBVR
U701: SN74LVC1G11DBVR; MPN SN74LVC1G11DBVR
U802, U803: CA-IS3417WT; MPN CA-IS3417WT
X501, X502, X503, X504: 006710340; MPN 006710340

Connections:
+3V3: C603.1, C604.1, C605.1, C608.1, C609.1, C702.1, C703.1, C802.1, R513.1, U601.8 (V+), U602.8 (V+), U603.5 (VCC), U604.8 (V+), U605.8 (V+), U701.5 (VCC), U701.6 (C), U702.5 (VCC), U801.8 (V+)
+5V: R816.1, R826.1
+24V: Q703.3 (S), Q705.3 (S), R709.1, R721.1
AGND: C603.2, C604.2, C605.2, C608.2, C609.2, C702.2, C703.2, C802.2, U501.3 (E), U601.4 (V-), U602.5 (V-), U603.3 (GND), U604.4 (V-), U605.3 (+INA), U605.4 (V-), U605.5 (+INB), U701.2 (GND), U702.3 (GND), U801.4 (V-), U801.5 (+INB)
A_HOLD_HI: U602.2 (-INA)
A_HOLD_LO: U602.3 (+INB)
A_IN+: R808.1
A_VMID: C606.2, C607.2, C801.2, R602.2, R606.2, R615.2, R622.2, R807.2
BUS-: R603.1, R607.1, R717.2, R818.1, RS601.2, RS602.2
B_BK+: K701.A2, R616.1, R710.1, R718.2
B_BL1: R710.2, R711.1
B_BL2: R711.2, R712.1
B_BL3: R712.2, R713.1
B_BL4: R713.2, R714.1
B_BL5: R714.2, R715.1
B_BL6: R715.2, R716.1
B_BL7: R716.2, R717.1
B_HOLD: U603.4 (Y), U701.1 (A)
B_HOLDN: U602.6 (OUTB), U603.2 (B)
B_HOLDP: U602.7 (OUTA), U603.1 (A)
B_IH: C602.2, R608.2, U601.7 (OUTB), U602.1 (+INA), U602.4 (-INB)
B_IM: C601.2, R604.2, U601.1 (OUTA)
B_IN+: F501.1, F503.1, X501.1
B_IN-: F502.1, F504.1, X503.1
B_K_COIL: C701.1, D702.2 (A), K701.1 (COIL1), Q703.2 (D)
B_K_G: Q702.1 (G), R707.1, U701.3 (B), U702.4 (Y)
B_K_GB: C701.2, D701.3 (K), Q701.1 (G), R705.1
B_K_H1: R701.2, R702.1
B_K_H2: R702.2, R703.1
B_K_H3: R703.2, R704.1
B_K_HG: U701.4 (Y), U702.2 (B)
B_K_LO: K701.2 (COIL2), Q701.3 (D), R701.1
B_K_PD: Q702.3 (D), R708.1
B_K_PG: Q703.1 (G), R708.2, R709.2
B_K_Z: D702.1 (K), D703.1 (K)
B_MON1: R501.1, RV501.3 (MON)
B_MON2: R512.2, RV502.3 (MON)
B_MON3: D501.1 (A), RV503.3 (MON), U501.2 (K)
B_MONA: D501.3 (K), R506.2, U501.1 (A)
B_MR1: R501.2, R502.1
B_MR2: R502.2, R503.1
B_MR3: R503.2, R504.1
B_MR4: R504.2, R505.1
B_MR5: R505.2, R506.1
B_MS1: R507.2, R508.1
B_MS2: R508.2, R509.1
B_MS3: R509.2, R510.1
B_MS4: R510.2, R511.1
B_MS5: R511.2, R512.1
B_PRE_M: K702.4 (P2), K702.6 (P1)
B_PRE_R: K702.2 (P2-), R718.1
B_P_COIL: D704.2 (A), K702.1 (COIL), Q705.2 (D)
B_P_PD: Q704.3 (D), R720.1
B_P_PG: Q705.1 (G), R720.2, R721.2
B_P_Z: D704.1 (K), D705.1 (K)
B_SHAN: C601.1, R603.2, R604.1, U601.2 (-INA)
B_SHAP: R601.2, R602.1, U601.3 (+INA)
B_SHBN: C602.1, R607.2, R608.1, U601.6 (-INB)
B_SHBP: R605.2, R606.1, U601.5 (+INB)
B_SP+: F501.2, RV501.1 (L), X502.1
B_SP-: F502.2, RV502.1 (L), X504.1
B_SPARE: U605.1 (OUTA), U605.2 (-INA)
B_SPAREB: U605.6 (-INB), U605.7 (OUTB)
B_SPD_N: R513.2, U501.4 (C)
B_SPM: R507.1, RV501.2 (N), RV502.2 (N), RV503.1 (L)
B_T+: F503.2, K701.A1, K702.8 (P1+), R609.1
B_T-: F504.2, R601.1, R605.1, RS601.1, RS602.1
B_VBD: C607.1, R621.2, R622.1, U604.5 (+INB)
B_VBD_1: R616.2, R617.1
B_VBD_2: R617.2, R618.1
B_VBD_3: R618.2, R619.1
B_VBD_4: R619.2, R620.1
B_VBD_5: R620.2, R621.1
B_VB_O: U604.6 (-INB), U604.7 (OUTB)
B_VXD: C606.1, R614.2, R615.1, U604.3 (+INA)
B_VXD_1: R609.2, R610.1
B_VXD_2: R610.2, R611.1
B_VXD_3: R611.2, R612.1
B_VXD_4: R612.2, R613.1
B_VXD_5: R613.2, R614.1
B_VX_O: U604.1 (OUTA), U604.2 (-INA)
CMD_IMDN: Q802.1 (G), R827.1
CMD_IMDP: Q801.1 (G), R817.1
CMD_KB: R706.1, U702.1 (A)
CMD_PB: Q704.1 (G), R719.1
GND: D701.1 (A), D703.2 (A), D705.2 (A), K702.0 (COIL), Q701.2 (S), Q702.2 (S), Q704.2 (S), Q801.2 (S), Q802.2 (S), R704.2, R705.2, R706.2, R707.2, R719.2, R817.2, R827.2
IMDN_A: R826.2, U803.4 (ANODE)
IMDN_K: Q802.3 (D), U803.3 (CATHODE1), U803.5 (CATHODE2)
IMDN_R1: R818.2, R819.1
IMDN_R2: R819.2, R820.1
IMDN_R3: R820.2, R821.1
IMDN_R4: R821.2, R822.1
IMDN_R5: R822.2, R823.1
IMDN_R6: R823.2, R824.1
IMDN_R7: R824.2, R825.1
IMDN_S: R825.2, U803.11 (Drain1), U803.12 (Drain1)
IMDP_A: R816.2, U802.4 (ANODE)
IMDP_K: Q801.3 (D), U802.3 (CATHODE1), U802.5 (CATHODE2)
IMDP_R1: R808.2, R809.1
IMDP_R2: R809.2, R810.1
IMDP_R3: R810.2, R811.1
IMDP_R4: R811.2, R812.1
IMDP_R5: R812.2, R813.1
IMDP_R6: R813.2, R814.1
IMDP_R7: R814.2, R815.1
IMDP_S: R815.2, U802.11 (Drain1), U802.12 (Drain1)
IMD_AUXD: C801.1, R806.2, R807.1, U801.3 (+INA)
IMD_AUXD_1: R801.2, R802.1
IMD_AUXD_2: R802.2, R803.1
IMD_AUXD_3: R803.2, R804.1
IMD_AUXD_4: R804.2, R805.1
IMD_AUXD_5: R805.2, R806.1
IMD_AUX_O: U801.1 (OUTA), U801.2 (-INA)
IMD_SPARE: U801.6 (-INB), U801.7 (OUTB)
PE_D: R801.1
PE_T: RV503.2 (N), U802.9 (Drain2), U802.10 (Drain2), U803.9 (Drain2), U803.10 (Drain2)

Notes on the sheet:
AR FUSES (BATTERY-TYPE PORT)
TVT25751 x 3 (615 VDC, thermal link + monitor lead): MOV1 +/M, MOV2 -/M, MOV3 M/PE_T. Up,eff 3793 V pole-PE and pole-pole at In 3 kA (calc., <= 4.0 kV -> reinforced 6 kV / basic 4 kV, D-032); Imax 25 kA. Branch fuses ETI CH14x51 gPV 36 A 30 kA (L/R 2 ms). Monitor loop through both fuses and all thr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
HPE501/000B100-250 in both poles: breaks 1.25-50 kA only (partial range); the port OC trip and the contactor keep it out of 250 A-1.25 kA.
Terminal side B_IN+ / B_IN-, bank B_BK+. HPE501 250 A aR in both poles (breaks 1.25-50 kA only). Contactor opens <= 0.97 kA, held above (port_spec lean). Installation: upstream clears 967-1250 A within 0.26 s.
ON-BOARD SURGE PROTECTION: VARISTOR Y (IC-01, IC-12)
PORT B (BATTERY SOURCE), D-044 LEAN PORT
