vectivolt/PCM/hardware/PV-CTL/sheets/03_afe.kicad_sch

## KiCad design hardware/PV-CTL/sheets/03_afe.kicad_sch (2026-10-06)

Schematic: 03_afe.kicad_sch

Parts:
C301, C304, C313, C323, C324, C325, C326, C327, C328, C329, C330, C331: 100n 50V
C302: 2.2u 10V
C303: 1u 10V
C305, C307, C309, C311: 47p 50V
C306, C308, C310, C312, C314, C315, C316, C317, C318, C319, C320, C321, C322: 1n 50V
R301, R304, R306, R309, R311, R314, R316, R319, R330, R331, R332, R333, R338: 10.0k
R302, R307, R312, R317: 29.4k
R303, R308, R313, R318: 36.5k
R305, R310, R315, R320: 47R
R321, R322, R323, R324, R325, R326, R327, R328, R329: 100R
R334, R335, R336, R337: 4.99k
RT301: NCP15XH103F03RC; MPN NCP15XH103F03RC
U301: REF3030EAIDBZR; MPN REF3030EAIDBZR
U302: TLV9064IPWR; MPN TLV9064IPWR

Connections:
+3V3A: C301.1, C313.1, U301.1 (IN), U302.4 (V+)
GND: C301.2, C302.2, C303.2, C304.2, C305.2, C306.2, C307.2, C308.2, C309.2, C310.2, C311.2, C312.2, C313.2, C314.2, C315.2, C316.2, C317.2, C318.2, C319.2, C320.2, C321.2, C322.2, C323.2, C324.2, C325.2, C326.2, C327.2, C328.2, C329.2, C330.2, C331.2, R302.2, R307.2, R312.2, R317.2, RT301.2, U301.3 (GND), U302.11 (V-)
IA: R326.1
IA_ADC: C319.1, R326.2
IA_H: R328.1
IA_H_ADC: C321.1, R328.2
IB: R327.1
IB_ADC: C320.1, R327.2
IB_H: R329.1
IB_H_ADC: C322.1, R329.2
IL1: R301.1
IL1_ADC: C306.1, R305.2
IL1_B: R304.2, R305.1, U302.1 (OUT1)
IL1_N: R303.1, R304.1, U302.2 (IN1-)
IL1_P: C305.1, R301.2, R302.1, U302.3 (IN1+)
IL2: R306.1
IL2_ADC: C308.1, R310.2
IL2_B: R309.2, R310.1, U302.7 (OUT2)
IL2_N: R308.1, R309.1, U302.6 (IN2-)
IL2_P: C307.1, R306.2, R307.1, U302.5 (IN2+)
IL3: R311.1
IL3_ADC: C310.1, R315.2
IL3_B: R314.2, R315.1, U302.8 (OUT3)
IL3_N: R313.1, R314.1, U302.9 (IN3-)
IL3_P: C309.1, R311.2, R312.1, U302.10 (IN3+)
IL4: R316.1
IL4_ADC: C312.1, R320.2
IL4_B: R319.2, R320.1, U302.14 (OUT4)
IL4_N: R318.1, R319.1, U302.13 (IN4-)
IL4_P: C311.1, R316.2, R317.1, U302.12 (IN4+)
NTC1: C323.1, R330.2
NTC2: C324.1, R331.2
NTC3: C325.1, R332.2
NTC4: C326.1, R333.2
NTC5: C327.1, R334.2
NTC6: C328.1, R335.2
NTC7: C329.1, R336.2
NTC8: C330.1, R337.2
NTC_IN: C331.1, R338.2, RT301.1
VA: R321.1
VAX: R323.1
VAX_ADC: C316.1, R323.2
VA_ADC: C314.1, R321.2
VB: R322.1
VBX: R324.1
VBX_ADC: C317.1, R324.2
VB_ADC: C315.1, R322.2
VPE: R325.1
VPE_ADC: C318.1, R325.2
VREF: C302.1, C303.1, C304.1, R303.2, R308.2, R313.2, R318.2, R330.1, R331.1, R332.1, R333.1, R334.1, R335.1, R336.1, R337.1, R338.1, U301.2 (OUT)

Notes on the sheet:
3.0 V REFERENCE (REF3030E FROM +3V3A)
VA/VB/VAX/VBX/VPE = VMID + V/1203; IA/IB = VMID + 3.0 mV/A (+/-478 A); IA_H/IB_H = VMID + 1.0 mV/A. Anti-alias poles are on the power board; here 100 R / 1 nF C0G as the ADC charge bucket. The trip comparators take the PC net itself (no ADC kick-back on them).
INLET-AIR NTC (ON BOARD)
NTC INPUTS (10 K B25/100 3988 K TO AGND + 100 NF ON PV-PWR, BIASED HERE FROM VREF)
ILn = 2.5 V + 10.667 mV/A (STK-HO/A 75 on PV-PWR, 0.5-4.5 V, not ratiometric) -> 10.0k / 29.4k 0.1 % -> ILn_P (47 pF, a = 0.746): trip window (sheet 04) and the + input; Rg 36.5k to VREF, Rf 10.0k: ADC = 1.555 V + 10.14 mV/A (0.072 A/LSB, -153..+142 A) -> 47 R / 1 nF -> ADC + CMPSS. IL4 = 0 V on PV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
NTC1-4 heatsink sections (10.0k), NTC5-8 inductor windings (4.99k), 100 nF each. Open probe = 3.0 V: trips through the open-probe comparators (sheet 04); short = 0 V: trips as over-temperature.
INDUCTOR-CURRENT FRONT ENDS IL1-IL4 (TLV9064 GAIN STAGES)
POWER-BOARD ANALOG SIGNALS (VMID 1.641-1.651 V PER PORT, NOT ON PC)
Murata NCP15XH103F03RC, 10.0k from VREF; ADC only (fan law, derating).
Feeds VREFHI (pins 24/25, >= 2.2 uF), VDAC (pin 16, >= 1 uF), the NTC biases, the IL offset and the threshold ladders of sheet 04: ADC, CMPSS and hardware trips are ratiometric to one reference. It runs from VDDA, so it never sits above VDDA (SPRSP61C 6.12.1.4.2). Needs +3V3 >= 3.20 V (REF30E dropo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
