vectivolt/PCM/hardware/PV-CTL/sheets/04_trip.kicad_sch

## KiCad design hardware/PV-CTL/sheets/04_trip.kicad_sch (2026-10-06)

Schematic: 04_trip.kicad_sch

Parts:
C401, C402, C403, C404, C405, C406, C407, C408, C409, C410, C411, C412: 10n 50V
C413, C414, C415, C416, C417, C418, C419: 100n 50V
R401, R405, R409, R413: 715R
R402, R406, R410, R414: 19.1k
R403, R407, R411, R415: 20.0k
R404, R408, R412, R416: 1M
R417: 2.05k
R418: 11.3k
R419: 102k
R420: 10.0k
R421: 30.9k
R422: 1.15k
R423: 115R
R424: 13.7k
R425, R426: 10k
U401, U402, U403, U404, U405: TLV9024PWR; MPN TLV9024PWR
U406, U407: TLV9024PWR (PV-P100/110 only); MPN TLV9024PWR

Connections:
+3V3: C413.1, C414.1, C415.1, C416.1, C417.1, C418.1, C419.1, R425.1, R426.1, U401.3 (V+), U402.3 (V+), U403.3 (V+), U404.3 (V+), U405.3 (V+), U406.3 (V+), U407.3 (V+)
GND: C401.2, C402.2, C403.2, C404.2, C405.2, C406.2, C407.2, C408.2, C409.2, C410.2, C411.2, C412.2, C413.2, C414.2, C415.2, C416.2, C417.2, C418.2, C419.2, R403.2, R407.2, R411.2, R415.2, R418.2, R420.2, R422.2, R424.2, U401.12 (V-), U402.12 (V-), U403.12 (V-), U404.12 (V-), U405.12 (V-), U406.12 (V-), U407.9 (IN3+), U407.11 (IN4+), U407.12 (V-)
IL1R: R401.1
IL1_P: U401.4 (IN1-), U401.7 (IN2+)
IL2R: R405.1
IL2_P: U401.8 (IN3-), U401.11 (IN4+)
IL3R: R409.1
IL3_P: U402.4 (IN1-), U402.7 (IN2+)
IL4R: R413.1
IL4_P: U406.4 (IN1-), U406.7 (IN2+)
NTC1: U403.5 (IN1+), U404.8 (IN3-)
NTC2: U403.7 (IN2+), U404.10 (IN4-)
NTC3: U403.9 (IN3+), U405.4 (IN1-)
NTC4: U406.9 (IN3+), U406.10 (IN4-)
NTC5: U403.11 (IN4+), U405.6 (IN2-)
NTC6: U404.5 (IN1+), U405.8 (IN3-)
NTC7: U404.7 (IN2+), U405.10 (IN4-)
NTC8: U407.5 (IN1+), U407.6 (IN2-)
OC_N: R425.2, U401.1 (OUT2), U401.2 (OUT1), U401.13 (OUT4), U401.14 (OUT3), U402.1 (OUT2), U402.2 (OUT1), U406.1 (OUT2), U406.2 (OUT1)
OVT_N: R426.2, U402.13 (OUT4), U402.14 (OUT3), U403.1 (OUT2), U403.2 (OUT1), U403.13 (OUT4), U403.14 (OUT3), U404.1 (OUT2), U404.2 (OUT1), U404.13 (OUT4), U404.14 (OUT3), U405.1 (OUT2), U405.2 (OUT1), U405.13 (OUT4), U405.14 (OUT3), U406.13 (OUT4), U406.14 (OUT3), U407.1 (OUT2), U407.2 (OUT1)
TH_IL1_HI: C401.1, R401.2, R402.1, U401.5 (IN1+)
TH_IL1_LO: C402.1, R402.2, R403.1, R404.2, U401.6 (IN2-)
TH_IL2_HI: C403.1, R405.2, R406.1, U401.9 (IN3+)
TH_IL2_LO: C404.1, R406.2, R407.1, R408.2, U401.10 (IN4-)
TH_IL3_HI: C405.1, R409.2, R410.1, U402.5 (IN1+)
TH_IL3_LO: C406.1, R410.2, R411.1, R412.2, U402.6 (IN2-)
TH_IL4_HI: C407.1, R413.2, R414.1, U406.5 (IN1+)
TH_IL4_LO: C408.1, R414.2, R415.1, R416.2, U406.6 (IN2-)
TH_OPEN: C412.1, R423.2, R424.1, U404.9 (IN3+), U404.11 (IN4+), U405.5 (IN1+), U405.7 (IN2+), U405.9 (IN3+), U405.11 (IN4+), U406.11 (IN4+), U407.7 (IN2+)
TH_OTH: C410.1, R419.2, R420.1, U403.4 (IN1-), U403.6 (IN2-), U403.8 (IN3-), U406.8 (IN3-)
TH_OTL: C411.1, R421.2, R422.1, U403.10 (IN4-), U404.4 (IN1-), U404.6 (IN2-), U407.4 (IN1-)
TH_OV: C409.1, R417.2, R418.1, U402.9 (IN3+), U402.11 (IN4+)
VA: U402.8 (IN3-)
VB: U402.10 (IN4-)
VREF: R404.1, R408.1, R412.1, R416.1, R417.1, R419.1, R421.1, R423.1, U407.8 (IN3-), U407.10 (IN4-)

Notes on the sheet:
PHASE 4 - ASSEMBLY OPTION: FITTED ON PV-P100/110 ONLY
TH_OV: VA/VB 1075 V; TH_OTH: heatsink 87.9 C (PV-PWR: <= 89.9 C); TH_OTL: inductor 150 C; TH_OPEN 2.975 V: an NTC node above it is an open probe (cold limit -30 C).
PHASES 1-3 AND THE PORT VOLTAGES (FITTED ON EVERY BUILD)
ILnR - 715R - TH_ILn_HI - 19.1k - TH_ILn_LO - 20.0k - GND: the window follows the sensor's own zero (Vref 2.48-2.52 V is no longer an error term; Voe +/-10 mV is). 1 M from VREF to TH_ILn_LO: with the sensor dead (IL = ILR = 0 V) TH_ILn_LO stays ~30 mV above ILn_P and the phase trips. Phase 4: fitt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
IL THRESHOLD LADDERS (0.1 %, 25 PPM/K), ONE PER PHASE FROM THAT SENSOR'S UREF (ILNR ON PC)
IL4 window, NTC4 / NTC8 over-temperature and open probe. Not fitted on PV-P75 (bom/PV-CTL-P75_BOM.csv), where IL4 = 0 V and NTC4 / NTC8 are open: nothing then pulls OC_N / OVT_N for phase 4. Fitted on a 4-phase build, a dead IL4 sensor (0 V) or an open NTC4 / NTC8 trips (fail-safe). Firmware cross-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
OC_N (wired-OR, 10k to +3V3): ILn_P above TH_ILn_HI or below TH_ILn_LO, n = 1-3. OVT_N (10k): VA, VB above TH_OV; NTC1-3 (heatsink) below TH_OTH, NTC5-7 (inductor) below TH_OTL; any of them above TH_OPEN. Port over-current (387-413 A) arrives on FLT_N from the power board's own comparators (PV-PWR).
THRESHOLD LADDERS (0.1 %, 25 PPM/K, FROM VREF)
