vectivolt/PCM/hardware/PV-CTL/sheets/08_eth.kicad_sch

## KiCad design hardware/PV-CTL/sheets/08_eth.kicad_sch (2026-10-06)

Schematic: 08_eth.kicad_sch

Parts:
C801, C806, C807: 1u 16V; not fitted
C802: 10u 10V; not fitted
C803, C805: 100n 50V; not fitted
C804: 1u 10V; not fitted
D801: SRV05-4; MPN SRV05-4; not fitted
J801: HR913550AE; MPN HR913550AE; not fitted
R801: 10R; not fitted
R802: 1.0k; not fitted
R803: 2.0k; not fitted
R804, R805: 470R; not fitted
TP801: TP
U801: TPS7A2033PDBVR; MPN TPS7A2033PDBVR; not fitted
U802: CH9121T; MPN CH9121T; not fitted
Y801: X322525MOB4SI; MPN X322525MOB4SI; not fitted

Connections:
PE: J801.8 (CHS_GND), J801.SH (SHIELD)
S_3V3: C802.1, C803.1, C805.1, D801.5 (Vcc), R804.1, R805.1, U801.5 (OUT), U802.8 (VCCIO), U802.18 (VCC33)
S_5V: R801.1
S_ETH_5V: C801.1, R801.2, U801.1 (IN), U801.3 (EN)
S_ETH_ACT: J801.11 (LEDY_K), U802.7 (ACT)
S_ETH_ACT_A: J801.12 (LEDY_A), R805.2
S_ETH_CFG: TP801.1, U802.11 (CFG)
S_ETH_LINK: J801.10 (LEDG_K), U802.6 (LINK/RESET)
S_ETH_LINK_A: J801.9 (LEDG_A), R804.2
S_ETH_RCT: C807.1, J801.5
S_ETH_RXD: R802.2, R803.1, U802.13 (RXD1)
S_ETH_RXD5: R802.1
S_ETH_RXN: D801.6 (IO4), J801.6 (RD-), U802.20 (RXN)
S_ETH_RXP: D801.4 (IO3), J801.3 (RD+), U802.19 (RXP)
S_ETH_TCT: C806.1, J801.4
S_ETH_TXD: U802.14 (TXD1)
S_ETH_TXN: D801.3 (IO2), J801.2 (TD-), U802.2 (TXN)
S_ETH_TXP: D801.1 (IO1), J801.1 (TD+), U802.1 (TXP)
S_ETH_VDDK: C804.1, U802.3 (VDDK)
S_ETH_XI: U802.4 (XI), Y801.1
S_ETH_XO: U802.5 (XO), Y801.3
S_GND: C801.2, C802.2, C803.2, C804.2, C805.2, C806.2, C807.2, D801.2 (GND), R803.2, U801.2 (GND), U802.17 (GND), Y801.2 (G), Y801.4 (G)

Notes on the sheet:
VCC33 needs 3.2-3.4 V (CH9121 V2.6 table 7-2): +/-1.5 % LDO. The 10R 1206 takes ~1 V of the drop so the LDO stays below 125 C at an 85 C board (design check). EN tied to IN. 1 uF in, 10 uF + 100 nF out.
RJ45 WITH MAGNETICS (HR913550AE), MDI PROTECTION, LINK / ACTIVITY LEDS
Chip side straight to the CH9121T (50 R inside: no 49.9 R); centre taps P4 / P5 to S_GND through 1 uF (maker: no supply on them). Bob-Smith 4 x 75 R + 1000 pF / 2 kV inside, CHS GND and the shield legs to PE (as the bus terminals' screen pins). SRV05-4 on the chip side (0.8 pF). LEDs: green = link,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
CH9121T (CH9121 V2.6 FIGURE 9-1)
SELV 3.3 V: TPS7A2033 FROM S_5V THROUGH 10R
Port 1 (RXD1 / TXD1) to SCIB through the CA-IS3842HW (sheet 06); port 2, CTS, TNOW open. 25 MHz 12 pF crystal, no load C (inside); VDDK 1 uF; power-on reset inside. Straps (pull-ups inside): CFG low at power-up = serial set-up (end-of-line test point); LINK/RESET low for 2 s = factory reset - its L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
