vectivolt/PCM/hardware/PV-PORT-180/sheets/01_io.kicad_sch

## KiCad design hardware/PV-PORT-180/sheets/01_io.kicad_sch (2026-10-04)

Schematic: 01_io.kicad_sch

Parts:
C101: 4.7u 50V
C102: 220n 50V
C103: 100n 50V
C104: 1u 16V
C105, C106: 22u 10V
J101: X9555WV-2x13-6TV01; MPN X9555WV-2x13-6TV01
J102: 691322310014; MPN 691322310014
L101: 74439346100; MPN 74439346100
MH101: PE bond M4
R101: 28k
R102, R103: 118k
R104, R105: 42.2k
R106: 100k
R107: 43.2k
R108: 0R
U101: LMR36015ARNXR; MPN LMR36015ARNXR

Connections:
+3V3S: C105.1, C106.1, L101.2, R106.1
+24V: C101.1, C102.1, J101.1, J101.2, U101.2 (VIN), U101.9 (EN), U101.10 (VIN)
AGND: J101.13, J101.14, J101.23, J101.24, R108.1
AUX1_N: J101.20
AUX1_P: J101.19
AUX2_N: J101.22
AUX2_P: J101.21
A_HC2_OC: R103.1
A_RB1: R102.1
B_HC2_OC: R105.1
B_RB1: R104.1
DO_SPARE: J102.8
FB_A_MAIN: J102.9
FB_B_MAIN: J102.11
GND: C101.2, C102.2, C104.2, C105.2, C106.2, J101.3, J101.4, J101.26, J102.10, J102.12, J102.13, J102.14, R101.2, R107.2, R108.2, U101.1 (PGND), U101.6 (AGND), U101.11 (PGND)
IA_N: J101.16
IA_P: J101.15
IB_N: J101.18
IB_P: J101.17
ID: J101.25, R101.1, R102.2, R103.2, R104.2, R105.2
IMD_SW_N: J102.7
IMD_SW_P: J102.6
K_A_MAIN: J102.2
K_A_PRE: J102.1
K_B_MAIN: J102.4
K_B_PRE: J102.3
K_DISCH: J102.5
PE: MH101.1
SS_BOOT: C103.1, U101.4 (BOOT)
SS_FB: R106.2, R107.1, U101.7 (FB)
SS_SW: C103.2, L101.1, U101.12 (SW)
SS_VCC: C104.1, U101.5 (VCC)
VAX_N: J101.8
VAX_P: J101.7
VA_N: J101.6
VA_P: J101.5
VBX_N: J101.12
VBX_P: J101.11
VB_N: J101.10
VB_P: J101.9

Notes on the sheet:
Board PE to chassis at the SPD / Y-capacitor end.
PE BOND
PORT CONNECTOR (CTRL-C2000) + ID WITH HOLD READBACK
port.CTRL_PINS: DO1-DO8 (DO_SPARE = proof test), FB_A + its GND, FB_B + its GND (INT-02), 2 coil returns. Port B (battery) drives 2 HVC43 coils: K_B_MAIN up to 0.60 A -> SYS DO4 needs ILIM 10 k (1.58-2.30 A).
CONTROL CONNECTOR (SYS-IO-AUX)
LMR36015 400 kHz, 24 V -> 3.315 V (100 k / 43.2 k, SNVSB49D sec 10.2), <= 0.34 A for 6 x AMC3330 + 2 x AMC3302 + hold logic. AGND joins GND only here (0 ohm).
interfaces.PORT, ribbon 1:1. AMC outputs drive the cable directly (<= 500 pF, AMC3330 p4); anti-alias RC is on CTRL-C2000. ID: 28k || readback network = 9.99 k (PV-PORT code 10.0k; CTRL-C2000 rev D values). RB outputs through 2 x 118k (port A) and 2 x 42.2k (port B): nine states, >= 155 counts apar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
SENSOR SUPPLY +3V3S
