vectivolt/PCM/hardware/PV-PORT-180/sheets/02_portA_power.kicad_sch

## KiCad design hardware/PV-PORT-180/sheets/02_portA_power.kicad_sch (2026-10-05)

Schematic: 02_portA_power.kicad_sch

Parts:
C201, C202: X 2.2u 1300V RFQ
C203, C204: VY1472M63Y5UQ63V0; MPN VY1472M63Y5UQ63V0
C205: 270n 25V
C206, C207: 100n 25V
C208: 1u 50V
C209: 1n 50V
D201, D207, D208, D209: BAS16; MPN BAS16
D202, D203, D205: S2M-13-F; MPN S2M-13-F
D204: SMBJ33A; MPN SMBJ33A
D206: BZX84-C15; MPN BZX84-C15
F201, F202: HP10NH2GPV250; MPN HP10NH2GPV250
F203, F204: 36A gPV 14x51; MPN 002637115
J201: DC terminal + (CUSTOM)
J202: DC terminal - (CUSTOM)
J203: KF2EDGR-3.5-2P; MPN KF2EDGR-3.5-2P
J204, J205, J206: 7461057; MPN 7461057
K201: B88269X7340C011; MPN B88269X7340C011
K202: G7L-2A-X DC24; MPN G7L-2A-X DC24
L201: CM choke 200 A (CUSTOM)
LK201: PE_T link to chassis PE: removable strap, OPEN fo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
Q201, Q204, Q207: IRFL214TRPbF; MPN IRFL214TRPbF
Q202, Q205, Q206, Q209: BSS138BK; MPN BSS138BK
Q203: IRFR9214TRPbF; MPN IRFR9214TRPbF
Q208: C2M1000170D; MPN C2M1000170D
Q210, Q211: MMBT3906-7-F; MPN MMBT3906-7-F
Q212: MMBT3904,215; MPN MMBT3904,215
R201, R202, R203, R204, R205, R206, R207, R208, R209, R210, R211, R212: 82.5k
R213: 220k
R214: 1.5k
R215, R217, R218, R219, R223: 10k
R216, R220, R224: 22k
R221, R222, R236, R243, R244, R245, R246, R247, R248, R249, R250, R251, R252: 47k
R225: 220R RST200 RFQ
R226, R227: 300R RST200 RFQ
R228, R229, R230, R231, R232: FVF06FT-2004; MPN FVF06FT-2004
R233, R234, R242: 100k
R235: 7.32k
R237, R238, R240, R241: 1M
R239: 4.7M
RS201: CSM2F-8518-L100J01; MPN CSM2F-8518-L100J01
RT201: B57703M0103A018; MPN B57703M0103A018
RV201, RV202, RV203: TVT25751KFKG; MPN TVT25751KFKG
RV204: B72210S0300K101; MPN B72210S0300K101
S201: KSD301 NO 80C RFQ
U201: CNY65B; MPN CNY65B
U202: TPSI3050QDWZRQ1; MPN TPSI3050QDWZRQ1
X201, X202, X203, X204: 006710340; MPN 006710340

Connections:
+3V3S: R213.1
+24V: Q203.3 (S), R214.1, R218.1
AGND: U201.3 (E)
A_BL1: R243.2, R244.1
A_BL2: R244.2, R245.1
A_BL3: R245.2, R246.1
A_BL4: R246.2, R247.1
A_BL5: R247.2, R248.1
A_BL6: R248.2, R249.1
A_BL7: R249.2, R250.1
A_BL8: R250.2, R251.1
A_BL9: R251.2, R252.1
A_BUS+: J204.1, K201.A2, R225.2, R226.1, R228.1, R243.1
A_DIS_B1: R228.2, R229.1
A_DIS_B2: R229.2, R230.1
A_DIS_B3: R230.2, R231.1
A_DIS_B4: R231.2, R232.1
A_DIS_D: Q208.2 (D), R227.2
A_DIS_EN: D207.3 (K), D208.3 (K), R234.1, U202.1 (EN)
A_DIS_G: D206.3 (K), Q208.1 (G), Q209.3 (D), Q211.2 (E), R232.2, R237.1, R239.1, R240.1, S201.1 (A)
A_DIS_M: R226.2, R227.1
A_DIS_OFF: Q209.1 (G), R233.1, U202.8 (VDRV)
A_DIS_PX: R235.1, U202.2 (PXFR)
A_DIS_REF: Q210.1 (B), R237.2, R238.1
A_DIS_SB: Q211.1 (B), Q212.3 (C), R240.2
A_DIS_SG: C209.1, Q210.3 (C), Q211.3 (C), Q212.1 (B), R241.1, R242.2
A_DIS_T: C208.1, D209.1 (A), R239.2
A_DIS_TE: D209.3 (K), Q210.2 (E)
A_DIS_TH: R242.1, S201.2 (B)
A_DIS_VDDH: C206.1, U202.7 (VDDH)
A_DIS_VDDM: C206.2, C207.1, U202.6 (VDDM)
A_DIS_VDDP: C205.1, U202.3 (VDDP)
A_F+: C201.1, F201.2, L201.1 (A1)
A_F-: C201.2, F202.2, L201.3 (B1)
A_HC1_HOLD: Q202.1 (G)
A_HC2_HOLD: Q206.1 (G)
A_HC_G2: Q204.1 (G), Q205.3 (D), R219.2, R220.1
A_HC_OUT: D203.2 (A), Q203.2 (D), R219.1, R221.1
A_HC_PD: Q202.3 (D), R217.1
A_HC_PG: Q203.1 (G), R217.2, R218.2
A_HC_X: Q205.1 (G), Q206.3 (D), R221.2, R222.1
A_IN+: F201.1, F203.1, J201.1, X201.1
A_IN-: F202.1, F204.1, J202.1, X203.1
A_KM_COIL: D202.1 (K), D203.1 (K), K201.2 (COIL+), RV204.1
A_KM_G1: Q201.1 (G), R215.2, R216.1
A_KM_LO: K201.3 (COIL-), Q201.2 (D), Q204.2 (D), RV204.2
A_KP_G: Q207.1 (G), R223.2, R224.1
A_KP_LO: D204.1 (K), K202.0 (COIL), Q207.2 (D)
A_KP_Z: D204.2 (A), D205.2 (A)
A_MON1: R201.1, RV201.3 (MON)
A_MON2: R212.2, RV202.3 (MON)
A_MON3: D201.1 (A), RV203.3 (MON), U201.2 (K)
A_MONA: D201.3 (K), R206.2, U201.1 (A)
A_MR1: R201.2, R202.1
A_MR2: R202.2, R203.1
A_MR3: R203.2, R204.1
A_MR4: R204.2, R205.1
A_MR5: R205.2, R206.1
A_MS1: R207.2, R208.1
A_MS2: R208.2, R209.1
A_MS3: R209.2, R210.1
A_MS4: R210.2, R211.1
A_MS5: R211.2, R212.1
A_PRE_M: K202.4 (P2), K202.6 (P1)
A_PRE_R: K202.2 (P2-), R225.1
A_SH_N: RS201.3 (SENSE1)
A_SH_P: RS201.4 (SENSE2)
A_SP+: F203.2, RV201.1 (L), X202.1
A_SP-: F204.2, RV202.1 (L), X204.1
A_SPD_N: R213.2, U201.4 (C)
A_SPM: R207.1, RV201.2 (N), RV202.2 (N), RV203.1 (L)
A_X+: C202.1, C203.1, J206.1, K201.A1, K202.8 (P1+), L201.2 (A2)
A_X-: C202.2, C204.1, L201.4 (B2), RS201.1 (BOLT1)
BUS-: C207.2, C208.2, C209.2, D206.1 (A), J205.1, Q208.3 (S), Q209.2 (S), Q212.2 (E), R233.2, R238.2, R241.2, R252.2, RS201.2 (BOLT2), U202.5 (VSSS)
FB_A_MAIN: D208.1 (A), K201.4 (AUX_NC), R214.2
GND: C205.2, K201.1 (AUX_COM), Q201.3 (S), Q202.2 (S), Q204.3 (S), Q205.2 (S), Q206.2 (S), Q207.3 (S), R216.2, R220.2, R222.2, R224.2, R234.2, R235.2, R236.2, U202.4 (VSSP)
K_A_MAIN: D202.2 (A), R215.1
K_A_PRE: D205.1 (K), K202.1 (COIL), R223.1
K_DISCH: D207.1 (A), R236.1
NTC_A_1: J203.1, RT201.1
NTC_A_2: J203.2, RT201.2
PE: LK201.2 (PE)
PE_T: C203.2, C204.2, LK201.1 (PE_T), RV203.2 (N)

Notes on the sheet:
FAIL-SAFE ACTIVE DISCHARGE, INHIBITED WHILE THE CONTACTOR IS CLOSED
TVT25751 x 3 (615 VDC, thermal link + monitor lead): MOV1 +/M, MOV2 -/M, MOV3 M/PE_T. Up,eff 3793 V pole-PE and pole-pole at In 3 kA (calc., <= 4.0 kV -> reinforced 6 kV / basic 4 kV, D-032); Imax 25 kA. Branch fuses ETI CH14x51 gPV 36 A 30 kA (L/R 2 ms). Monitor loop through both fuses and all thr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
PASSIVE BLEEDER + BOARD CONNECTION POINTS
G7L-2A-X, poles in series, normal polarity = current 8 -> 2 (terminal -> bus). K_A_PRE feeds the coil and gates its IRFL214 low side; S2M + SMBJ33A across the coil (37-42 V, Omron p5). R_pre 220 ohm Miba RST 200 (RFQ, pulse-rated). Complete at |dV| <= 10 V after the VA/VAX null; abort below 0.8 x V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
HOLD-CLOSED POWER STAGE (2 INDEPENDENT CHANNELS)
HVC43-250A-24MC, + pole, bidirectional (TDK p2). Opens at zero current in normal operation; cut-off 450 A @ 1000 V once. K_A_MAIN feeds coil+ (S2M) AND gates the IRFL214 low side: two switches in the path. S10K30 directly across the coil = the only flyback path (>= 54 V down to drop-out; TDK p7 >= 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
TPSI3050 EN = K_DISCH OR FB_A_MAIN (2 x BAS16): powered = BSS138 holds the SiC gate low. Unpowered = the bus biases the gate (10 M, 15 V zener) -> 2 x 300 ohm Miba RST 200 discharge the bus. FB is high while the contactor is closed (or welded), so an E-stop or a lost K_DISCH cannot discharge a live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
10 x 47 k 2512 1 W (100 V each at 1000 V): back-up discharge, 2.4 W at 1000 V. REDCUBE studs: bus +/- to the power cells, terminal-side tap.
MOV3, Y capacitors and the IMD test strings return on PE_T: a removable M4 strap to chassis PE, opened for the hipot. Open strap = no IMD swing.
SHUNT (- POLE) + SHUNT NTC
DIS_G charges 1 uF through 4.7 M; a MMBT3906 compares it with DIS_G/2 (1 M / 1 M, also the gate pull- down) and fires the MMBT3906/MMBT3904 latch: gate clamped to 0.75 V after 2.4-5.1 s (needed <= 1.8 s), held by the bias current until K_DISCH returns (BSS138 resets it). Thermostat KSD301-class (cl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
TERMINALS, FUSES (PV-TYPE PORT)
Channel 1: HOLD1 -> BSS138 -> IRFR9214 high side from the port +24V (not cut by E-stop) -> S2M -> coil+. Channel 2: IRFL214 low side coil- -> GND, gate fed from the channel-1 output (10 k / 22 k) and clamped off by a BSS138 unless HOLD2: it can only conduct while channel 1 conducts, so no flyback e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
X 2 x 2.2 uF film (RFQ: impulse >= 4.5 kV, PA-07), CM choke (CUSTOM), Y1 4.7 nF pole-PE (1500 VDC rated). Y capacitors are declared HV-PE crossings.
PRECHARGE RELAY + RESISTOR
ON-BOARD SURGE PROTECTION: VARISTOR Y (IC-01, IC-12)
CSM2F-8518 100 uOhm, busbar-mounted. Kelvin test points to the IA/IB amplifier. Positive current = power into the module at this port. NTC on the shunt (reinforced pad) -> SYS-IO-AUX NTC input: firmware TCR compensation.
PE LINK (IC-23, IMD LESSON 4)
EMI FILTER
DISCHARGE TIME LIMIT + THERMAL CUT-OFF (HV SIDE, NEEDS NO 24 V)
MAIN CONTACTOR: COIL DRIVE + FEEDBACK
CHASSIS-MOUNTED. 180 A port: gPV 250 A 1000 V DC in each pole, derated 194 A (fuses in the INLET air path, PD3: terminals / fuse bases only, creepage to PE >= 16.0 mm IIIa, IC-18/IC-21).
