vectivolt/PCM/hardware/PV-PORT-180/sheets/03_portA_sense.kicad_sch

## KiCad design hardware/PV-PORT-180/sheets/03_portA_sense.kicad_sch (2026-10-04)

Schematic: 03_portA_sense.kicad_sch

Parts:
C301, C310: 4.7n 50V
C302, C306, C309, C311, C315, C318, C320, C324, C327: 1n 50V
C303, C305, C312, C314, C321, C323: 1u 25V
C304, C307, C308, C313, C316, C317, C322, C325, C326, C328, C329, C330, C331, C332, C333, C334, C335, C336, C337, C338, C340, C342, C344, C345, C346: 100n 50V
C319: 10n 50V
C339: 22u 25V
C341, C343: 3.3u 25V
R301, R302, R303, R304, R305, R306, R308, R309, R310, R311, R312, R313: TNPV12061M00BEEA; MPN TNPV12061M00BEEA
R307, R314: TNPW12064K99BEEA; MPN TNPW12064K99BEEA
R315, R316: 10R
R317, R350, R351, R353: 47k
R318, R321, R324, R327, R333, R336, R339, R342: 49.9k
R319, R325, R334, R340: 118k
R320, R326, R335, R341: 86.6k
R322, R328, R337, R343: 88.7k
R323, R329, R338, R344: 113k
R330, R332, R345, R347, R348, R355: 100k
R331, R346: 25.5k
R349, R356: 15k
R352, R354: 10k
TP301, TP302: TP
U301, U302: AMC3330DWE; MPN AMC3330DWE
U303: AMC3302DWE; MPN AMC3302DWE
U304, U308: REF3030EAIDBZR; MPN REF3030EAIDBZR
U305, U309: TLV3502AIDCNR; MPN TLV3502AIDCNR
U306, U310, U316, U317: SN74LVC1G32DBVR; MPN SN74LVC1G32DBVR
U307, U311: SN74LVC1G11DBVR; MPN SN74LVC1G11DBVR
U312, U313, U314, U315: SN74LVC1G17DBVR; MPN SN74LVC1G17DBVR

Connections:
+3V3S: C302.1, C303.1, C311.1, C312.1, C320.1, C321.1, C328.1, C330.1, C331.1, C332.1, C333.1, C335.1, C336.1, C337.1, C338.1, C340.1, C342.1, C344.1, C345.1, C346.1, R317.2, U301.12 (VDD), U302.12 (VDD), U303.12 (VDD), U304.1 (IN), U305.8 (V+), U306.5 (VCC), U307.5 (VCC), U308.1 (IN), U309.8 (V+), U310.5 (VCC), U311.5 (VCC), U312.5 (VCC), U313.5 (VCC), U314.5 (VCC), U315.5 (VCC), U316.5 (VCC), U317.5 (VCC)
AGND: C302.2, C303.2, C304.2, C311.2, C312.2, C313.2, C320.2, C321.2, C322.2, C328.2, C329.2, C330.2, C331.2, C332.2, C333.2, C334.2, C335.2, C336.2, C337.2, C338.2, C339.2, C340.2, C342.2, C344.2, C345.2, C346.2, R319.2, R323.2, R325.2, R329.2, R331.2, R332.2, R334.2, R338.2, R340.2, R344.2, R346.2, R347.2, R349.2, R351.2, R353.2, R356.2, U301.9 (GND), U301.15 (DCDC_GND), U302.9 (GND), U302.15 (DCDC_GND), U303.9 (GND), U303.15 (DCDC_GND), U304.3 (GND), U305.5 (V-), U306.3 (GND), U307.2 (GND), U308.3 (GND), U309.5 (V-), U310.3 (GND), U311.2 (GND), U312.3 (GND), U313.3 (GND), U314.3 (GND), U315.3 (GND), U316.3 (GND), U317.3 (GND)
A_BUS+: R301.1
A_HC1_FB: R330.2, R331.1, U307.3 (B)
A_HC1_HOLD: R332.1, U307.4 (Y)
A_HC1_NA: R321.2, R322.1, R323.1, U305.2 (-INA)
A_HC1_NB: R327.2, R328.1, R329.1, U305.4 (-INB)
A_HC1_OC: U306.4 (Y), U307.1 (A), U316.1 (A)
A_HC1_OCN: U305.6 (OUTB), U306.2 (B)
A_HC1_OCP: U305.7 (OUTA), U306.1 (A)
A_HC1_PA: R318.2, R319.1, R320.2, U305.1 (+INA)
A_HC1_PB: R324.2, R325.1, R326.2, U305.3 (+INB)
A_HC1_REF: C329.1, R322.2, R328.2, U304.2 (OUT)
A_HC2_FB: R345.2, R346.1, U311.3 (B)
A_HC2_HOLD: R347.1, U311.4 (Y)
A_HC2_NA: R336.2, R337.1, R338.1, U309.2 (-INA)
A_HC2_NB: R342.2, R343.1, R344.1, U309.4 (-INB)
A_HC2_OC: TP302.1, U310.4 (Y), U311.1 (A)
A_HC2_OCN: U309.6 (OUTB), U310.2 (B)
A_HC2_OCP: U309.7 (OUTA), U310.1 (A)
A_HC2_PA: R333.2, R334.1, R335.2, U309.1 (+INA)
A_HC2_PB: R339.2, R340.1, R341.2, U309.3 (+INB)
A_HC2_REF: C334.1, R337.2, R343.2, U308.2 (OUT)
A_HC_OUT: R355.1
A_HC_OUTL: R355.2, R356.1, U316.2 (B)
A_RB1: TP301.1, U317.4 (Y)
A_RB1A: U316.4 (Y), U317.1 (A)
A_SH_N: R316.1
A_SH_P: R315.1
A_SPD_N: U317.2 (B)
A_TST_DRC: C339.1, R350.2, U313.2 (A)
A_TST_IN: R348.2, R349.1, U312.2 (A)
A_TST_T: C341.1, R320.1, R350.1, U312.4 (Y)
A_TST_T2A: R335.1, U314.4 (Y)
A_TST_T2B: R341.1, U315.4 (Y)
A_TST_TD: C343.1, R326.1, U313.4 (Y)
A_TST_XA: C341.2, R351.1, R352.1
A_TST_XAI: R352.2, U314.2 (A)
A_TST_XB: C343.2, R353.1, R354.1
A_TST_XBI: R354.2, U315.2 (A)
A_X+: R308.1
A_X-: C323.2, C324.2, C325.2, C326.2, C327.2, U303.2 (DCDC_HGND), U303.8 (HGND)
BUS-: C301.2, C305.2, C306.2, C307.2, C308.2, C309.2, C310.2, C314.2, C315.2, C316.2, C317.2, C318.2, R307.2, R314.2, U301.2 (DCDC_HGND), U301.7 (INN), U301.8 (HGND), U302.2 (DCDC_HGND), U302.7 (INN), U302.8 (HGND)
DO_SPARE: R348.1
FB_A_MAIN: R330.1, R345.1
IA_DCO: C323.1, C324.1, C325.1, U303.1 (DCDC_OUT), U303.3 (HLDO_IN)
IA_DIAG: R317.1, U303.14 (DIAG), U307.6 (C), U311.6 (C)
IA_HLDO: C326.1, C327.1, U303.5 (HLDO_OUT)
IA_INN: C319.2, R316.2, U303.7 (INN)
IA_INP: C319.1, R315.2, U303.6 (INP)
IA_LDO: C322.1, U303.13 (LDO_OUT), U303.16 (DCDC_IN)
IA_N: R321.1, R324.1, R336.1, R339.1, U303.10 (OUTN)
IA_P: R318.1, R327.1, R333.1, R342.1, U303.11 (OUTP)
VAX_D1: R308.2, R309.1
VAX_D2: R309.2, R310.1
VAX_D3: R310.2, R311.1
VAX_D4: R311.2, R312.1
VAX_D5: R312.2, R313.1
VAX_DCO: C314.1, C315.1, C316.1, U302.1 (DCDC_OUT), U302.3 (HLDO_IN)
VAX_HLDO: C317.1, C318.1, U302.5 (HLDO_OUT)
VAX_IN: C310.1, R313.2, R314.1, U302.6 (INP)
VAX_LDO: C313.1, U302.13 (LDO_OUT), U302.16 (DCDC_IN)
VAX_N: U302.10 (OUTN)
VAX_P: U302.11 (OUTP)
VA_D1: R301.2, R302.1
VA_D2: R302.2, R303.1
VA_D3: R303.2, R304.1
VA_D4: R304.2, R305.1
VA_D5: R305.2, R306.1
VA_DCO: C305.1, C306.1, C307.1, U301.1 (DCDC_OUT), U301.3 (HLDO_IN)
VA_HLDO: C308.1, C309.1, U301.5 (HLDO_OUT)
VA_IN: C301.1, R306.2, R307.1, U301.6 (INP)
VA_LDO: C304.1, U301.13 (LDO_OUT), U301.16 (DCDC_IN)
VA_N: U301.10 (OUTN)
VA_P: U301.11 (OUTP)

Notes on the sheet:
VA - BUS-SIDE VOLTAGE
|IA| > 410 A (band 382-441 A, own REF3030E + 0.1 % network, CM-cancelling) AND FB = closed AND DIAG = valid -> HOLD2. Test injection 86.6 k from A_TST_T2A (side A) / A_TST_T2B (side B): shifts the threshold by 459 A, so a healthy side trips at 0 A under TEST only.
HOLD-CLOSED LOGIC, CHANNEL 2 (IRFL214 LOW SIDE)
RB1 = OC1 OR hold high-side output present (100 k / 15 k): at rest RB1 = 1 means a stuck channel 1. RB2 = OC2. PV-PORT sums them onto the ID line (board_io); firmware reads RB1 + RB2 against the measured current in operation and through the proof-test windows at start.
6 x TNPV1206 1.00 M (167 V each at 1000 V) + 4.99 k: 1 V = 1203 V, clip 1504 V. 4.7 nF: lag <= 27 us incl. AMC3330. Out: VAX_P/N (+/-2 V on 1.44 V, PORT contract). HGND = BUS-.
PROOF-TEST INJECTION (DO_SPARE = TEST)
HOLD-CLOSED LOGIC, CHANNEL 1 (IRFR9214 HIGH SIDE)
READBACK RB1 / RB2 (TO CTRL ON A SPARE LINE)
Linear +/-500 A, clip +/-640 A (OC trip 270 A, SC trip 450 A inside). 10 ohm + 10 nF input filter (SBASA11B Fig 8-2). HGND on the shunt's X- bolt by its own trace. Fail-safe out = -2.57 V.
100 k / 15 k -> Schmitt buffer T (ch1 side A). T -> 47 k / 22 uF -> T_d (ch1 side B). One-shots (3.3 uF / 47 k) of T -> T2A (ch2 side A) and of T_d -> T2B (ch2 side B). No single fault trips both channels for longer than one one-shot. Firmware runs it at every start, contactor open and closed (repo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
VAX - TERMINAL-SIDE VOLTAGE
|IA| > 410 A (band 382-441 A, own REF3030E + 0.1 % network, CM-cancelling) AND FB = closed AND DIAG = valid -> HOLD1. Test injection 86.6 k from A_TST_T (side A) / A_TST_TD (side B): shifts the threshold by 459 A, so a healthy side trips at 0 A under TEST only.
6 x TNPV1206 1.00 M (167 V each at 1000 V) + 4.99 k: 1 V = 1203 V, clip 1504 V. 4.7 nF: lag <= 27 us incl. AMC3330. Out: VA_P/N (+/-2 V on 1.44 V, PORT contract). HGND = BUS-.
IA - PORT CURRENT
