vectivolt/PCM/hardware/PV-PORT-180/sheets/04_portB_power.kicad_sch

## KiCad design hardware/PV-PORT-180/sheets/04_portB_power.kicad_sch (2026-10-05)

Schematic: 04_portB_power.kicad_sch

Parts:
C401, C402: X 2.2u 1300V RFQ
C403, C404: VY1472M63Y5UQ63V0; MPN VY1472M63Y5UQ63V0
C405: 270n 25V
C406, C407: 100n 25V
C408: 1u 50V
C409: 1n 50V
D401, D403, D404, D405, D406, D411, D412, D413: BAS16; MPN BAS16
D402, D407, D409: S2M-13-F; MPN S2M-13-F
D408: SMBJ33A; MPN SMBJ33A
D410: BZX84-C15; MPN BZX84-C15
F401, F402: 004110760; MPN 004110760
F403, F404: 36A gPV 14x51; MPN 002637115
J401: DC terminal + (CUSTOM)
J402: DC terminal - (CUSTOM)
J403: KF2EDGR-3.5-2P; MPN KF2EDGR-3.5-2P
J404, J405, J406: 7461057; MPN 7461057
K401, K402: B88269X7340C011; MPN B88269X7340C011
K403: G7L-2A-X DC24; MPN G7L-2A-X DC24
L401: CM choke 200 A (CUSTOM)
LK401: PE_T link to chassis PE: removable strap, OPEN fo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
Q401, Q402, Q405, Q406, Q409: IRFL214TRPbF; MPN IRFL214TRPbF
Q403, Q407, Q408, Q411: BSS138BK; MPN BSS138BK
Q404: IRFR9214TRPbF; MPN IRFR9214TRPbF
Q410: C2M1000170D; MPN C2M1000170D
Q412, Q413: MMBT3906-7-F; MPN MMBT3906-7-F
Q414: MMBT3904,215; MPN MMBT3904,215
R401, R402, R403, R404, R405, R406, R407, R408, R409, R410, R411, R412: 82.5k
R413: 220k
R414, R415, R420: 1.5k
R416, R418, R422, R423, R424, R428: 10k
R417, R419, R425, R429: 22k
R421, R438, R439, R447: 100k
R426, R427, R441, R448, R449, R450, R451, R452, R453, R454, R455, R456, R457: 47k
R430: 220R RST200 RFQ
R431, R432: 300R RST200 RFQ
R433, R434, R435, R436, R437: FVF06FT-2004; MPN FVF06FT-2004
R440: 7.32k
R442, R443, R445, R446: 1M
R444: 4.7M
RS401: CSM2F-8518-L100J01; MPN CSM2F-8518-L100J01
RT401: B57703M0103A018; MPN B57703M0103A018
RV401, RV402, RV403: TVT25751KFKG; MPN TVT25751KFKG
RV404, RV405: B72210S0300K101; MPN B72210S0300K101
S401: KSD301 NO 80C RFQ
U401: CNY65B; MPN CNY65B
U402: TPSI3050QDWZRQ1; MPN TPSI3050QDWZRQ1
X401, X402, X403, X404: 006710340; MPN 006710340

Connections:
+3V3S: R413.1
+24V: Q404.3 (S), R414.1, R415.1, R420.1, R423.1
AGND: U401.3 (E)
BUS-: C407.2, C408.2, C409.2, D410.1 (A), J405.1, Q410.3 (S), Q411.2 (S), Q414.2 (E), R438.2, R443.2, R446.2, R457.2, RS401.2 (BOLT2), U402.5 (VSSS)
B_BL1: R448.2, R449.1
B_BL2: R449.2, R450.1
B_BL3: R450.2, R451.1
B_BL4: R451.2, R452.1
B_BL5: R452.2, R453.1
B_BL6: R453.2, R454.1
B_BL7: R454.2, R455.1
B_BL8: R455.2, R456.1
B_BL9: R456.2, R457.1
B_BUS+: J404.1, K401.A2, K402.A2, R430.2, R431.1, R433.1, R448.1
B_DIS_B1: R433.2, R434.1
B_DIS_B2: R434.2, R435.1
B_DIS_B3: R435.2, R436.1
B_DIS_B4: R436.2, R437.1
B_DIS_D: Q410.2 (D), R432.2
B_DIS_EN: D411.3 (K), D412.3 (K), R439.1, U402.1 (EN)
B_DIS_G: D410.3 (K), Q410.1 (G), Q411.3 (D), Q413.2 (E), R437.2, R442.1, R444.1, R445.1, S401.1 (A)
B_DIS_M: R431.2, R432.1
B_DIS_OFF: Q411.1 (G), R438.1, U402.8 (VDRV)
B_DIS_PX: R440.1, U402.2 (PXFR)
B_DIS_REF: Q412.1 (B), R442.2, R443.1
B_DIS_SB: Q413.1 (B), Q414.3 (C), R445.2
B_DIS_SG: C409.1, Q412.3 (C), Q413.3 (C), Q414.1 (B), R446.1, R447.2
B_DIS_T: C408.1, D413.1 (A), R444.2
B_DIS_TE: D413.3 (K), Q412.2 (E)
B_DIS_TH: R447.1, S401.2 (B)
B_DIS_VDDH: C406.1, U402.7 (VDDH)
B_DIS_VDDM: C406.2, C407.1, U402.6 (VDDM)
B_DIS_VDDP: C405.1, U402.3 (VDDP)
B_F+: C401.1, F401.2, L401.1 (A1)
B_F-: C401.2, F402.2, L401.3 (B1)
B_FB1: D403.3 (K), D404.1 (A), K401.4 (AUX_NC), R414.2
B_FB2: D405.3 (K), D406.1 (A), K402.4 (AUX_NC), R415.2
B_FB_ANY: D404.3 (K), D406.3 (K), D412.1 (A), R421.1
B_HC1_HOLD: Q403.1 (G)
B_HC2_HOLD: Q408.1 (G)
B_HC_G2: Q405.1 (G), Q406.1 (G), Q407.3 (D), R424.2, R425.1
B_HC_OUT: D407.2 (A), Q404.2 (D), R424.1, R426.1
B_HC_PD: Q403.3 (D), R422.1
B_HC_PG: Q404.1 (G), R422.2, R423.2
B_HC_X: Q407.1 (G), Q408.3 (D), R426.2, R427.1
B_IN+: F401.1, F403.1, J401.1, X401.1
B_IN-: F402.1, F404.1, J402.1, X403.1
B_KM_COIL: D402.1 (K), D407.1 (K), K401.2 (COIL+), K402.2 (COIL+), RV404.1, RV405.1
B_KM_G1A: Q401.1 (G), R416.2, R417.1
B_KM_G1B: Q402.1 (G), R418.2, R419.1
B_KM_LO: K401.3 (COIL-), K402.3 (COIL-), Q401.2 (D), Q402.2 (D), Q405.2 (D), Q406.2 (D), RV404.2, RV405.2
B_KP_G: Q409.1 (G), R428.2, R429.1
B_KP_LO: D408.1 (K), K403.0 (COIL), Q409.2 (D)
B_KP_Z: D408.2 (A), D409.2 (A)
B_MON1: R401.1, RV401.3 (MON)
B_MON2: R412.2, RV402.3 (MON)
B_MON3: D401.1 (A), RV403.3 (MON), U401.2 (K)
B_MONA: D401.3 (K), R406.2, U401.1 (A)
B_MR1: R401.2, R402.1
B_MR2: R402.2, R403.1
B_MR3: R403.2, R404.1
B_MR4: R404.2, R405.1
B_MR5: R405.2, R406.1
B_MS1: R407.2, R408.1
B_MS2: R408.2, R409.1
B_MS3: R409.2, R410.1
B_MS4: R410.2, R411.1
B_MS5: R411.2, R412.1
B_PRE_M: K403.4 (P2), K403.6 (P1)
B_PRE_R: K403.2 (P2-), R430.1
B_SH_N: RS401.3 (SENSE1)
B_SH_P: RS401.4 (SENSE2)
B_SP+: F403.2, RV401.1 (L), X402.1
B_SP-: F404.2, RV402.1 (L), X404.1
B_SPD_N: R413.2, U401.4 (C)
B_SPM: R407.1, RV401.2 (N), RV402.2 (N), RV403.1 (L)
B_X+: C402.1, C403.1, J406.1, K401.A1, K402.A1, K403.8 (P1+), L401.2 (A2)
B_X-: C402.2, C404.1, L401.4 (B2), RS401.1 (BOLT1)
FB_B_MAIN: D403.1 (A), D405.1 (A), R420.2
GND: C405.2, K401.1 (AUX_COM), K402.1 (AUX_COM), Q401.3 (S), Q402.3 (S), Q403.2 (S), Q405.3 (S), Q406.3 (S), Q407.2 (S), Q408.2 (S), Q409.3 (S), R417.2, R419.2, R421.2, R425.2, R427.2, R429.2, R439.2, R440.2, R441.2, U402.4 (VSSP)
K_B_MAIN: D402.2 (A), R416.1, R418.1
K_B_PRE: D409.1 (K), K403.1 (COIL), R428.1
K_DISCH: D411.1 (A), R441.1
NTC_B_1: J403.1, RT401.1
NTC_B_2: J403.2, RT401.2
PE: LK401.2 (PE)
PE_T: C403.2, C404.2, LK401.1 (PE_T), RV403.2 (N)

Notes on the sheet:
MAIN CONTACTOR: COIL DRIVE + FEEDBACK
FB_B_MAIN (SYS DI) = BOTH contactors closed: own 1.5 k pull-up, a BAS16 to each mirror node, so a contactor that failed to close is seen at once (the single-contactor state is not coordinated). The hold logic and the TPSI3050 EN use B_FB_ANY = ANY closed (BAS16 diode-OR): a single welded contactor 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
PRECHARGE RELAY + RESISTOR
ON-BOARD SURGE PROTECTION: VARISTOR Y (IC-01, IC-12)
PASSIVE BLEEDER + BOARD CONNECTION POINTS
10 x 47 k 2512 1 W (100 V each at 1000 V): back-up discharge, 2.4 W at 1000 V. REDCUBE studs: bus +/- to the power cells, terminal-side tap.
TVT25751 x 3 (615 VDC, thermal link + monitor lead): MOV1 +/M, MOV2 -/M, MOV3 M/PE_T. Up,eff 3793 V pole-PE and pole-pole at In 3 kA (calc., <= 4.0 kV -> reinforced 6 kV / basic 4 kV, D-032); Imax 25 kA. Branch fuses ETI CH14x51 gPV 36 A 30 kA (L/R 2 ms). Monitor loop through both fuses and all thr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
Channel 1: HOLD1 -> BSS138 -> IRFR9214 high side from the port +24V (not cut by E-stop) -> S2M -> coil+. Channel 2: IRFL214 low side coil- -> GND, gate fed from the channel-1 output (10 k / 22 k) and clamped off by a BSS138 unless HOLD2: it can only conduct while channel 1 conducts, so no flyback e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
DIS_G charges 1 uF through 4.7 M; a MMBT3906 compares it with DIS_G/2 (1 M / 1 M, also the gate pull- down) and fires the MMBT3906/MMBT3904 latch: gate clamped to 0.75 V after 2.4-5.1 s (needed <= 1.8 s), held by the bias current until K_DISCH returns (BSS138 resets it). Thermostat KSD301-class (cl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
G7L-2A-X, poles in series, normal polarity = current 8 -> 2 (terminal -> bus). K_B_PRE feeds the coil and gates its IRFL214 low side; S2M + SMBJ33A across the coil (37-42 V, Omron p5). R_pre 220 ohm Miba RST 200 (RFQ, pulse-rated). Complete at |dV| <= 10 V after the VA/VAX null; abort below 0.8 x V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
X 2 x 2.2 uF film (RFQ: impulse >= 4.5 kV, PA-07), CM choke (CUSTOM), Y1 4.7 nF pole-PE (1500 VDC rated). Y capacitors are declared HV-PE crossings.
HOLD-CLOSED POWER STAGE (2 INDEPENDENT CHANNELS)
TERMINALS, FUSES (BATTERY-TYPE PORT)
CHASSIS-MOUNTED. 180 A port: ETI gBat (30 kA at L/R 1 ms) 200 A 1000 V DC in each pole, derated 136 A (fuses in the INLET air path, PD3: terminals / fuse bases only, creepage to PE >= 16.0 mm IIIa, IC-18/IC-21). FIRMWARE CURRENT LIMIT (D-020): 180/180/180/172/164/155/146/136 A at inlet 25/30/35/40/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
DISCHARGE TIME LIMIT + THERMAL CUT-OFF (HV SIDE, NEEDS NO 24 V)
TPSI3050 EN = K_DISCH OR FB_B_MAIN (2 x BAS16): powered = BSS138 holds the SiC gate low. Unpowered = the bus biases the gate (10 M, 15 V zener) -> 2 x 300 ohm Miba RST 200 discharge the bus. FB is high while the contactor is closed (or welded), so an E-stop or a lost K_DISCH cannot discharge a live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
EMI FILTER
FAIL-SAFE ACTIVE DISCHARGE, INHIBITED WHILE THE CONTACTOR IS CLOSED
MOV3, Y capacitors and the IMD test strings return on PE_T: a removable M4 strap to chassis PE, opened for the hipot. Open strap = no IMD swing.
SHUNT (- POLE) + SHUNT NTC
CONTACTOR PAIR FEEDBACK (BATTERY-TYPE PORT)
PE LINK (IC-23, IMD LESSON 4)
HVC43-250A-24MC, + pole, bidirectional (TDK p2). Opens at zero current in normal operation; cut-off 450 A @ 1000 V once. K_B_MAIN feeds coil+ (S2M) AND gates the IRFL214 low side: two switches in the path. S10K30 directly across the coil = the only flyback path (>= 54 V down to drop-out; TDK p7 >= 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
CSM2F-8518 100 uOhm, busbar-mounted. Kelvin test points to the IA/IB amplifier. Positive current = power into the module at this port. NTC on the shunt (reinforced pad) -> SYS-IO-AUX NTC input: firmware TCR compensation.
