vectivolt/PCM/gen/pv_power.py

"""PV-PWR / PV-PWR-4 - POWER board of the cost-first PV module (decision D-044, docs/requirements/ARCHITECTURE-COSTFIRST.md
sections 1, 3-6, 8-11): ONE board with every phase (3 for PV-P75, 4 for PV-P100/110) and everything that is not the
controller. All of it is live and referenced to BUS- (GND = AGND = BUS-, joined at one star point); other domains are
only the gate-drive islands (functional), the AUX-T1 reinforced SELV winding (leaves on a 2-pin connector) and PE.

  01        PC connector (interfaces.PC) to the control board, 3.3 -> 5 V command buffers (gdrv.input_buffers), RDY / FLT_N,
            +5 V supervisor, port status glue (HOLD, MOV_OK, port over-current into FLT_N), ground star points
  per phase power stage (2 x SG2M040170HJ per switch on AlN pads, film decoupling + RC damper per leg, the phase's share of
            the port banks), gate bias (gdrv.bias_phase), inductor (CUSTOM, chassis) through a Sinomags STK-HO/A 75
            open-loop current sensor, heatsink and inductor NTC inputs; two sheets of gdrv.channel(bias="ext") per phase
  ports     gen/port.py lean_port() A (PV) and B (battery), DC terminals, CM ring core, X/Y capacitors, insulation monitor
  supplies  +5V / +5V_GD (2 x LMR38020) from the live 24 V, +3V3 (TPS62130, controlled ramps), SELV connector
  aux       gen/aux_hv.py aux75_block(): 75 W flyback from both ports' terminal taps, live 24 V + reinforced SELV 24 V
Values are read at build time from sim/out/pv_design/cell_spec.json, pv_control/control_spec.json, pv_design/module_spec.json,
magnetics/design_pv_inductor.json and port_design/port_spec.json; design_check() asserts them on every build.
Usage: .venv/bin/python gen/pv_power.py      (builds PV-PWR and PV-PWR-4, each with its own checks and BOM)
Rev A2 (2026-10-05, D-056): PV-P75 battery-side film bank 7 x 45 uF (7th on phase 2), bleeders 8 x 73.2 k, STK Uref on PC (IL1R-IL4R).
"""
import hashlib
import json
import math
import os
import re
import sys

import numpy as np

import aux_hv
import catalog
import dcdclib as L
import gdrv
import interfaces as IF
import port
import pvcell

REV, DATE = "A2", "2026-10-05"
PROJECT = {3: "PV-PWR", 4: "PV-PWR-4"}
DS = "docs/datasheets/"
OUT = lambda *p: os.path.join(L.REPO, "sim", "out", *p)


SPEC = json.load(open(os.path.join(L.REPO, "sim", "out", "pv_design", "cell_spec.json")))   # LIVE cell spec (pvcell.SPEC is the earlier platform's frozen snapshot)                                                   # cell_spec.json (per phase = one former cell)
CTRL = json.load(open(OUT("pv_control", "control_spec.json")))
MODS = json.load(open(OUT("pv_design", "module_spec.json")))
MAG = json.load(open(OUT("magnetics", "design_pv_inductor.json")))   # read at build time: rev M1 / M2 / later
spec = pvcell.make_spec(SPEC)
# every spec file this board's numbers are read from (relative to the repository): the design check records their hashes, so that
# gen/pv_ctrl.py refuses a power-board check that was built from other versions (PCM-23)
STAMP_FILES = ("sim/out/pv_design/cell_spec.json", "sim/out/pv_control/control_spec.json", "sim/out/pv_design/module_spec.json",
               "sim/out/pv_design/report.md", "sim/out/magnetics/design_pv_inductor.json", "sim/out/port_design/port_spec.json",
               "sim/out/aux_hv_design/aux75_spec.json", "sim/out/gdrv_miller/result_primary.json", "sim/out/port_design/report.md")
FAN_FLOW_TOL = 0.03          # airflow reduction treated as inside the thermal margin (PCM-26); more than this derates module_spec

# ------------------------------------------------------------------------------------------------ catalog
MAG_ROW = MAG["cost"]["cost_estimates_row"].split(",")[0]
_el = MAG["electrical"]
L_DESC = ("CHASSIS-MOUNTED CUSTOM power inductor rev %s (sim/out/magnetics/design_pv_inductor.json, winding sheet "
          "sim/out/magnetics/spec_pv_inductor.md): %s. L0 %.0f uH, %.0f uH nom / %.0f uH min at 45 A, ripple %.1f App at "
          "%.0f kHz, %.2f kg, %s. Leads A (through the phase's STK-HO/A 75 on the board) and B on press-fit studs; "
          "embedded winding NTC to a 2-pin header (NTC line on PC); core and clamp bonded to PE (basic winding-core, "
          "B2): %s" % (MAG["revision"], MAG["construction"], _el["L0_H"] * 1e6, _el["L_at_45A_nom_H"] * 1e6,
                        _el["L_at_45A_min_H"] * 1e6, _el["ripple_pp_A"], _el["f_ripple_Hz"] / 1e3, MAG["mass_kg"],
                        MAG["status"], MAG["insulation"]["system"]))
PARTS = {
    # XKB X9555WV drawing (single page, docs/datasheets/connectors/XKB-X9555WV.pdf): poles 2x03 ... 2x32, 2.54 mm,
    # 250 V AC/DC, 3 A, 1000 V AC 1 min, -40..+125 C; odd/even numbering = KiCad Conn_02x32_Odd_Even (as the 2x20 / 2x13)
    "J_PC": dict(mfr="XKB Connection", mpn="X9555WV-2x32-6TV01", prefix="J", pkg="2x32 2.54 mm box header THT",
                 ds=DS + "connectors/XKB-X9555WV.pdf", stock=("Connector_Generic", "Conn_02x32_Odd_Even"),
                 desc="Shrouded box header 2x32 2.54 mm: PC contract to the control board, live (250 V, 3 A, -40..125 C)"),
    # Sinomags STK-HO/A series Ver1.5 (2026-08-31), Sinomags-STK-HO-A.pdf: p5 (sec. 3) STK-HO/A 75 data; p16 (PDF page
    # 17) 'Dimension & Pin definitions': 1 +Uc, 2 GND (- or 0 V), 3 Uout, 4 Uref (OUT), 5 NC; integrated U primary
    # pins 6-9 and 10-13 (body arrow: 6-9 -> 10-13 = positive output, verify at incoming inspection)
    "STK75": dict(mfr="Sinomags Technology", mpn="STK-HO/A 75", prefix="CS", pkg="PCB mount 35.4 x 25 x 21.7 mm, U-bar primary",
                  ds=DS + "sensing/Sinomags-STK-HO-A.pdf",
                  desc="Open-loop current sensor, integrated primary, IPN 75 A rms, IPM +/-187.5 A, 10.667 mV/A around "
                       "Vref 2.5 V at Vcc 5 V, 1 MHz, 0.2 us; 4 kV rms / 8 kV impulse, 13.8 mm creepage",
                  pins={"left": ["6 IP+ p", "7 IP+ p", "8 IP+ p", "9 IP+ p", None, "1 +UC pi", "2 GND pi"],
                        "right": ["10 IP- p", "11 IP- p", "12 IP- p", "13 IP- p", None, "3 UOUT o", "4 UREF o",
                                  "5 NC nc"]}),
    # Jianghai CBB 138 DS (Jianghai-JE26-Film.pdf p28-30, v2026.2), class A3: 1300 VDC <= 70 C / 1100 VDC <= 85 C hot
    # spot. Order-code letters as gen/aux_hv.py (K = 10 %, pin style 0, 5.0 mm pins) - confirm with Jianghai.
    "FILM45": dict(mfr="Jianghai", mpn="FCSA3DS456K050H8F9DE3", prefix="C", pkg="4-pin 57.5 x 35 x 70 mm, P1 52.5 / P2 20.3",
                   ds=DS + "passives-capacitors/Jianghai-JE26-Film.pdf", stock=("Device", "C"),
                   desc="DC-link PP film 45 uF 10 %, 1300 VDC (70 C) / 1100 VDC (85 C), Imax 22.1 A (85 C) / 29.0 A (70 C) "
                        "at 10 kHz, peak 900 A, ESR 4.0 mOhm, Ls 35 nH, IEC 61071 (port bank)"),
    "FILM2U2": dict(mfr="Jianghai", mpn="FCSA3DS225K050IC90BE3", prefix="C", pkg="2-pin 32 x 14 x 28 mm, pitch 27.5 mm",
                    ds=DS + "passives-capacitors/Jianghai-JE26-Film.pdf", stock=("Device", "C"),
                    desc="PP film 2.2 uF 10 %, 1300 VDC (70 C) / 1100 VDC (85 C), Imax 3.9 A (85 C) / 5.2 A (70 C), peak "
                         "176 A, ESR 22.5 mOhm, Ls 25 nH, 80 V/us (leg decoupling)"),
    "L_PV": dict(mfr="", mpn="", prefix="L", pkg="chassis, 2 power leads + NTC leads + core clamp", ds="", sourcing="CUSTOM",
                 desc=L_DESC, pins={"left": ["1 A p", None, "3 NTC1 p"], "right": ["2 B p", None, "4 NTC2 p", "5 CORE p"]}),
    # Heatsink NTC: no Asian probe with a stated >= 2.2 kV rms lead-to-lug rating was found on file (R-10): made to order
    "NTC_HS": dict(mfr="", mpn="", prefix="RT", pkg="ring-lug probe M4, 2 x 300 mm PTFE leads", ds="", sourcing="CUSTOM",
                   desc="CHASSIS CUSTOM NTC lug probe (EXSENSE / Shiheng class, made to order): 10 k 1 %, R/T curve of the "
                        "inductor NTC (B25/100 3988 K, TDK 8016 equivalent), -40..150 C, lug screwed to the EARTHED "
                        "heatsink: lead-to-lug dielectric >= 2500 V rms 60 s, double PTFE leads (basic HV-PE for 1000 V "
                        "DC, insulation_spec 'Basic HV-PE', R-10)",
                   pins={"left": ["1 T1 p", "2 T2 p"], "right": ["3 LUG p"]}),
    "HEATSINK": dict(mfr="", mpn="", prefix="HS", pkg="Al extrusion, 2 device rows", ds="", sourcing="CUSTOM",
                     desc="CHASSIS CUSTOM heatsink: one Al extrusion for all devices (two rows: leg A, leg B), EARTHED (two "
                          "PE bonds >= 6 mm2), R_sa <= 0.06 K/W at 400 m3/h (PV-P75) / 0.049 K/W (PV-P100/110), with the "
                          "TO-247 spring clips (one per device, on the plastic body) and G-779-class grease (two bond "
                          "lines per AlN pad)", pins={"left": ["1 PE p"]}),
    # Qingdao Yunlu nanocrystalline core manual (Yunlu-Nanocrystalline-Cores.pdf, ring table): N-C-644025 64/40/25 mm,
    # cased 67/37/29 mm, Ae 225 mm2, le 160.4 mm. The standard high-mu grade (mu_i 70000 / 24000) is REJECTED by the magnetics
    # design (sim/out/magnetics/spec_port_cm_choke.md rev M2, D-048): it saturates with the 150 Hz common-mode current; the part
    # is the flat-permeability grade (mu about 30000 at 150 Hz, Shincore SC-1K107-LP class or the Yunlu / AT&M flat grade, catalogue
    # p.6) - an RFQ item keyed by the size code (review R4 / E12 found the BOM text naming the high-mu grade)
    "CM_RING": dict(mfr="Qingdao Yunlu (flat-mu grade) / Shincore / AT&M", mpn="N-C-644025", prefix="L", sourcing="RFQ",
                    pkg="ring 67/37/29 mm cased, on both port conductors", ds=DS + "magnetics/Yunlu-Nanocrystalline-Cores.pdf",
                    desc="CHASSIS nanocrystalline ring core 64/40/25 mm (cased), FLAT-PERMEABILITY grade mu about 30000 at 150 Hz "
                         "(Shincore SC-1K107-LP class or Yunlu / AT&M flat grade; the standard high-mu 70000 grade is rejected - it "
                         "saturates with the 150 Hz CM current, spec_port_cm_choke.md rev M2): one turn of BOTH conductors of the port "
                         "= CM choke for 150 kHz-30 MHz (ARCHITECTURE 8.1); pins = conductors",
                    pins={"left": ["1 A1 p", "3 B1 p"], "right": ["2 A2 p", "4 B2 p"]}),
}
PARTS["J_NTC2"] = dict(port.CATALOG["J_NTC"], desc="NTC leads (heatsink probe / inductor winding NTC), 2-pin pluggable")
PARTS["J_SELV"] = dict(port.CATALOG["J_NTC"], desc="SELV 24 V (AUX-T1 reinforced winding) to the control board's SELV zone: "
                                                  ">= 10 mm from live copper, double-insulated wires (ARCHITECTURE 10, J2)")
PICK_PVCELL = ("SG2M040170HJ", "PAD_ALN", "R_DAMP", "AHCT1G08", "TPS3710", "NETTIE")
CATALOG = {**catalog.PARTS, **gdrv.PARTS, **port.CATALOG, **{k: pvcell.CATALOG[k] for k in PICK_PVCELL},
           **{k: sys.modules["ctrl_c2000"].PARTS[k] for k in ("LMR38020", "L15U", "TPS62130", "L2U2")}, **PARTS}

# ------------------------------------------------------------------------------------------------ design inputs
N_PAR = spec("switch_positions", 0, "parallel")
R_GATE = (spec("switch_positions", 0, "gate_resistor_on_ohm"), spec("switch_positions", 0, "gate_resistor_off_ohm"))
GATE_V = (spec("gate_drive", "V_GS_on_V"), -spec("gate_drive", "V_GS_off_V"))
VCLASS, R_SB = pvcell.VCLASS, pvcell.R_SB
V_PEAK = spec("switch_node_recurring_peak", "at_1100V_trip_V")
DT = (pvcell.DT_R, 100e-12)                    # interlock stretch, as PVCELL-25 rev C0 (window checked at this board's 5 V)
NEG_DET = True   # gdrv rev 9 defaults it OFF, but its simulation shows a lost negative rail is NOT caught by DESAT
#                  (~+5.1 V at the die, ~1.6 mJ per event, ~50 W at 32 kHz, undetected): the detector is fitted here
V_OVP = spec("protection", "overvoltage_hw_trip_port_A_V")
FB5 = (100e3, 24.9e3)                          # LMR38020 RFBT / RFBB 0.1 % (ctrl_c2000 circuit, SNVSC40E table 9-1)
V5 = (0.985 * (1 + FB5[0] * 0.999 / (FB5[1] * 1.001)), 1.015 * (1 + FB5[0] * 1.001 / (FB5[1] * 0.999)))   # VREF p6
FB33 = (31.6e3, 10.0e3)                        # TPS62130 FB divider 0.1 % -> 3.328 V nominal
V33 = (0.7816 * (1 + FB33[0] * 0.999 / (FB33[1] * 1.001)) * 0.999 - 100e-9 * FB33[0],
       0.8224 * (1 + FB33[0] * 1.001 / (FB33[1] * 0.999)) * 1.001 + 100e-9 * FB33[0])
#   +3V3: TPS62130 SLVSAG7F p5 VFB 781.6-822.4 mV in power-save mode (785.6-814.4 PWM), FB leakage <= 100 nA, +/-0.1 %
#   line/load (as gen/ctrl_c2000.py supervisor()); control board: >= 3.20 V (its reference dropout)
SS33 = 470e-12                                 # TPS62130 SS/TR capacitor, C0G 5 %: sets the +3V3 ramp-up (F28003x SRVDDIO)
R_DIS33 = 1.2                                  # +3V3 discharge resistor (2512): sets the ramp-down when the rails fail
S75 = json.load(open(aux_hv.SPEC75_PATH))      # 75 W aux block (gen/aux_hv.py aux75_block), read at build time
V24 = tuple(S75["regulation"]["live_V"])       # live 24 V window of the aux block
assert gdrv.V5_RANGE[0] <= V5[0] and V5[1] <= gdrv.V5_RANGE[1], "+5V outside the range gdrv's bias numbers assume"
SUP_DIV = (107e3, 10.0e3)                      # +5V -> TPS3710 SENSE: RDY low below 4.52-4.69 V (AHCT VCC min 4.5 V)


DEC_N = spec("decoupling", "count_per_leg")
BANK_N = spec("capacitors", "port_A", "count")       # per phase and port (cell_spec)
BANK_XTRA = {3: {"B": 2}}                           # rev A2 (D-056): PV-P75's 7th battery-side capacitor, on phase 2


def bank_n(n_ph, t, p):
    """FCSA3DS456 count of port t ('A' / 'B') at phase p (module_spec costfirst port_film_bank sets the minimum)."""
    return BANK_N + (1 if BANK_XTRA.get(n_ph, {}).get(t) == p else 0)


def bank_total(n_ph, t):
    return sum(bank_n(n_ph, t, p) for p in range(1, n_ph + 1))
DAMP_R, DAMP_PAR, DAMP_SER = pvcell.DAMP_R, pvcell.DAMP_PAR, pvcell.DAMP_SER
DAMP_C = pvcell.DAMP_C                         # (value per element, elements in series)
HS_PAD = spec("heatsink_insulator")


def pwm(p, k):
    """PC contract: phase p, switch Sk -> PWM(4(p-1)+k)."""
    return "PWM%d" % (4 * (p - 1) + k)


def pos(p, s):
    """(drain, power source, complementary switch) of switch s in phase p: leg A = S1/S2 on port A, leg B = S3/S4."""
    a, b = "SW_A%d" % p, "SW_B%d" % p
    return {"S1": ("A_BUS+", a, "S2"), "S2": (a, "BUS-", "S1"), "S3": ("B_BUS+", b, "S4"), "S4": (b, "BUS-", "S3")}[s]


def tag(p, s):
    return "P%d%s" % (p, s)


def v5_of(p):
    """Gate-bias primary rail of phase p: phases 1-2 on +5V (with the logic), 3-4 on +5V_GD (second LMR38020)."""
    return "+5V" if p <= 2 else "+5V_GD"


def en_of(p):
    """SN6505B enable of phase p, buffered from the same rail as its VCC (SLLSEP9I abs max: EN <= VCC + 0.5 V)."""
    return "BIAS_EN5" if p <= 2 else "BIAS_EN5G"


# ------------------------------------------------------------------------------------------------ sheets
def sheet_pc(B, n_ph):
    """PC connector, command level shift, RDY / FLT_N, +5 V supervisor, ground star points."""
    B.new_sheet("01_pc", "PC connector, command buffers, status",
                "interfaces.PC (2x32) to the control board, 3.3 -> 5 V command buffers,\n"
                "RDY / FLT_N, +5 V supervisor, port status glue, BUS- star points")
    nc = {"NTC4", "NTC8"} | {pwm(4, k) for k in range(1, 5)} if n_ph == 3 else set()
    B.block("PC connector (interfaces.PC), live",
            "Both boards live: GND = AGND = BUS-. +3V3 goes TO the control board (rev A2: the former +24V / +5V pins carry\n"
            "the sensor references IL1R-IL4R). Commands are 3.3 V logic after the control board's trip latch; every command\n"
            "input is pulled low here (open = off).%s"
            % ("\nPV-P75: PWM13-16, NTC4 and NTC8 not connected; IL4 and IL4R pulled to AGND (0 V = no phase 4)."
               if n_ph == 3 else ""))
    pins = IF.pins(IF.PC, rename=PC_RENAME)
    B.part("J_PC", {k: (None if v in nc else v) for k, v in pins.items()})
    B.C("10u", "+3V3", "GND", pkg="1210", volt="16V")
    B.C("100n", "+3V3", "GND", volt="50V")
    B.block("Command inputs: pull-downs and 3.3 -> 5 V buffers (gdrv.input_buffers)",
            "NSI6651 inputs are specified at VCC1 = 5 V only (VINH <= 3.5 V, p7) and the SN6505B EN needs 0.7 VCC: one\n"
            "SN74AHCT1G08 (VIH 2.0 V) per line. Each PWM is ANDed with EN here as well, so a low EN removes every\n"
            "command within 8 ns, ahead of the drivers' RST/EN filter (0.48-0.8 us).")
    for net in ["EN", "BIAS_EN"] + [pwm(p, k) for p in range(1, n_ph + 1) for k in range(1, 5)]:
        B.R("10k", net, "GND", note="pull-down: open = off")
    pairs = [("EN", "EN5", None), ("BIAS_EN", "BIAS_EN5", None)] + \
            [(pwm(p, k), pwm(p, k) + "_5V", "EN") for p in range(1, n_ph + 1) for k in range(1, 5)]
    gdrv.input_buffers(B, pairs, v5="+5V", gnd="GND", part="AHCT1G08")
    if n_ph > 2:     # phases 3-4: SN6505B on +5V_GD, so their enable comes from a buffer on that rail
        gdrv.input_buffers(B, [("BIAS_EN", "BIAS_EN5G", None)], v5="+5V_GD", gnd="GND", part="AHCT1G08")
    B.R("10k", "EN5", "GND", note="pull-down: unpowered buffer = drivers disabled")
    B.block("RDY (wired-AND) and FLT_N (wired-OR)",
            "RDY: every NSI6651 RDY (VCC1 and VCC2 UVLO), the +5V and +5V_GD supervisors and the aux status (live 24 V\n"
            "UV), pulled up HERE to +3V3 (4.99k). FLT_N: every NSI6651 /FLT + port OC; pull-up on the control board.\n"
            "+5V supervisor TPS3710 %s/%s: RDY low below %.2f-%.2f V (AHCT VCC >= 4.5 V, bias headroom)."
            % (gdrv.ohm(SUP_DIV[0]), gdrv.ohm(SUP_DIV[1]), *sup_window()[0]))
    B.R("4.99k", "+3V3", "RDY", note="RDY pull-up (power board)")
    B.C("100p", "RDY", "GND", diel="C0G", tol="5%")
    B.C("100p", "FLT_N", "GND", diel="C0G", tol="5%")
    B.part("TPS3710", {"5": "+5V", "3": "SUP5_SNS", "1": "RDY", "2": "GND", "4": "GND", "6": "GND"})
    B.C("100n", "+5V", "GND")
    B.R(gdrv.ohm(SUP_DIV[0]), "+5V", "SUP5_SNS", tol="0.1%")
    B.R(gdrv.ohm(SUP_DIV[1]), "SUP5_SNS", "GND", tol="0.1%")
    B.C("1n", "SUP5_SNS", "GND")
    if n_ph == 3:
        B.R("10k", "IL4", "AGND", note="PV-P75 variant code: IL4 = 0 V (a fitted sensor reads >= 0.5 V)")
        B.R("10k", "IL4R", "AGND", note="PV-P75: no phase-4 sensor reference")
    B.block("Port status to PC: HOLD, MOV_OK, port over-current into FLT_N",
            "HOLD = A_HOLD OR B_HOLD (|I_port| >= 0.97-1.03 kA, contactor held). MOV_OK high only while BOTH varistor\n"
            "monitor loops conduct (each reads 'open' below ~200 V on its port). Port OC (|I| >= 387-413 A, lean_shunt)\n"
            "pulls FLT_N low (open drain): the control board's latch trips without firmware (aR-fuse gap, port_spec).\n"
            "K_A / K_B / K_PRE pulled low: open = coil off (the hardware interlocks follow on the port sheets).")
    B.part("LVC1G32", {"1": "A_HOLD", "2": "B_HOLD", "5": "+3V3", "4": "HOLD", "3": "GND"})
    B.C("100n", "+3V3", "GND")
    B.R("10k", "+3V3", "MOV_OK", note="high = both varistor monitor loops intact")
    for g, d in (("A_SPD_N", "MOV_OK"), ("B_SPD_N", "MOV_OK"), ("A_OC", "FLT_N"), ("B_OC", "FLT_N")):
        B.part("BSS138BK", {"1": g, "3": d, "2": "GND"})
    for net in ("K_A", "K_B", "K_PRE"):
        B.R("100k", net, "GND", note="open = coil off")
    B.block("Ground star points", "AGND meets GND at one point; GND meets BUS- at one point next to the port shunts\n"
                                  "(controller ground = BUS-). Layout: gate-drive primaries decoupled to GND locally.")
    B.part("NETTIE", {"1": "AGND", "2": "GND"})
    B.part("NETTIE", {"1": "GND", "2": "BUS-"})
    for net in ("+5V", "+3V3", "GND", "AGND"):          # +24V no longer on this sheet (rev A2: not on PC)
        B.flag(net)


# PC contract name -> this board's net: the port functions (gen/port.py lean_*) name their outputs <port>_<signal>
PC_RENAME = {"IA": "A_IM", "IA_H": "A_IH", "IB": "B_IM", "IB_H": "B_IH", "VA": "A_VB_O", "VAX": "A_VX_O", "VB": "B_VB_O",
             "VBX": "B_VX_O", "VPE": "IMD_AUX_O"}


def sheets_ports(B, n_ph, st):
    """Port A (PV) and port B (battery) with gen/port.py lean_port(), then terminals, CM rings, X/Y capacitors, board
    entries, PE links and the insulation monitor (lean_imd) on one sheet."""
    no = 2 + 3 * n_ph
    dom, xing = st["dom"], st["xing"]
    pa = port.lean_port(B, "A", "pv", no, "A_IN+", "A_IN-", "A_BUS+", "BUS-", "K_A", dom=dom, xing=xing)
    pb = port.lean_port(B, "B", "battery", no + 2, "B_IN+", "B_IN-", "B_BUS+", "BUS-", "K_B", cmd_pre="K_PRE", dom=dom,
                        xing=xing)
    st["ports"] = (pa, pb)
    rating = {3: 135, 4: 180}[n_ph]
    term = {135: "TERM200", 180: "TERM250"}[rating]
    B.new_sheet("%02d_terminals_imd" % (no + 4), "Terminals, EMI filter, insulation test",
                "DC terminals, nanocrystalline CM ring per port, X / Y capacitors, board\n"
                "entries (press-fit), PE links, heatsink, insulation monitor (port.lean_imd)")
    for t in ("A", "B"):
        B.block("Port %s terminals and EMI filter" % t,
                "%s: chassis terminals %s_TERM+/- (%d A port), both conductors once through the N-C-644025 ring (CM, 150 kHz-\n"
                "30 MHz, ARCHITECTURE 8.1), X 2.2 uF 1300 V at the varistor network, Y1 4.7 nF pole-PE_T (removable PE link\n"
                "for the hipot). Board taps %s_IN+%s by short links." % ({"A": "PV", "B": "battery"}[t], t, rating, t,
                                                                       "" if t == "A" else " / B_IN- / B_T+"))
        for pol in "+-":
            B.part(term, {"1": "%s_TERM%s" % (t, pol)}, value="DC terminal %s %d A (CUSTOM)" % (t + pol, rating))
        B.part("CM_RING", {"1": t + "_TERM+", "2": t + "_IN+", "3": t + "_TERM-", "4": t + "_IN-"})
        B.part("XCAP_2U2", {"1": t + "_IN+", "2": t + "_IN-"}, value="X 2.2u 1300V RFQ")
        for pol in "+-":
            xing.add(B.part("VY1_4N7", {"1": t + "_IN" + pol, "2": "PE_T"}).ref)
    B.block("Board entries (Wurth REDCUBE press-fit M3, 100 A each)",
            "Bus entries from the contactors / fuses: A_BUS+, B_BUS+, A_IN- and B_T- (into the shunts), two studs each;\n"
            "taps A_IN+, B_IN+, B_IN-, B_T+ (varistors, dividers, IMD, precharge, aux input), one each.")
    for net, k in (("A_BUS+", 2), ("B_BUS+", 2), ("A_IN-", 2), ("B_T-", 2), ("A_IN+", 1), ("B_IN+", 1), ("B_IN-", 1),
                   ("B_T+", 1)):
        for _ in range(k):
            B.part("STUD", {"1": net})
    B.block("PE: links, heatsink", "PE_T (Y capacitors, MOV3, IMD strings) reaches PE through a removable strap (open for the\n"
                                   "hipot, IC-23); PE_D = IMD divider bond; the heatsink is earthed at two points.")
    B.part("PE_LINK", {"1": "PE_T", "2": "PE"})
    B.part("PE_BOND", {"1": "PE_D"}, value="PE bond M4 (IMD divider reference)")
    B.part("PE_BOND", {"1": "PE"}, value="PE bond M4 (board PE)")
    B.part("HEATSINK", {"1": "PE"}, value="heatsink %d x TO-247 (CUSTOM)" % (8 * n_ph))
    B.block("Insulation monitor (port.lean_imd)", "IMD_SW1 = string A+ -> PE, IMD_SW2 = string PE -> BUS- (high = connected);\n"
                                                  "VPE = PE divider against BUS- (VMID of port A).")
    port.lean_imd(B, "A_IN+", "BUS-", "PE_T", "PE_D", pa["refs"], "IMD_SW1", "IMD_SW2", "+5V", "GND", "+3V3", "AGND", dom, xing)
    nets = B.D.nets()
    for c, n in PC_RENAME.items():
        assert n in nets, "PC %s: port function no longer drives %s" % (c, n)


def sheet_power(B, p, st):
    """Phase p: legs A/B (2 x SG2M040170HJ per switch on AlN pads), film decoupling + RC damper per leg, the phase's
    share of both port banks, inductor through the current sensor, NTC inputs, per-phase gate bias."""
    sa, sb, la = "SW_A%d" % p, "SW_B%d" % p, "L_A%d" % p
    B.new_sheet("%02d_ph%d_power" % (2 + 3 * (p - 1), p), "Phase %d power stage, bias, sensing" % p,
                "Legs A/B (2 x SG2M040170HJ per switch), decoupling, dampers, bank share,\n"
                "inductor + STK-HO/A 75, NTC inputs, gate bias (gdrv.bias_phase)")
    for leg, (top, bot), bus in (("A", ("S1", "S2"), "A_BUS+"), ("B", ("S3", "S4"), "B_BUS+")):
        B.block("Phase %d leg %s: %s (top) / %s (bottom), %d x SG2M040170HJ each" % (p, leg, top, bot, N_PAR),
                "Kelvin source (pin 3) of each device to its own driver COM star (gate-drive sheet). Each tab on its own\n"
                "%s pad to the EARTHED heatsink (basic HV-PE, B2). LAYOUT (IC-22): milled slot between drain pin 1 and\n"
                "pins 2-4; equal drain / source busbar paths for the two devices of a switch."
                % HS_PAD["material"].split(",")[0])
        for s in (top, bot):
            drain, source, _ = pos(p, s)
            for d in "ab"[:N_PAR]:
                st["xing"].add(B.part("SG2M040170HJ", {"1": drain, "5": drain, "2": source, "3": "KS_%s%s" % (tag(p, s), d),
                                                       "4": "G_%s%s" % (tag(p, s), d)}).ref)
                st["iso"].add(B.part("PAD_ALN", {"1": drain, "2": "PE"},
                                     value="PAD AlN %g mm (CUSTOM)" % HS_PAD["thickness_mm"]).ref)
        d1, d2, d3 = ("DMP_%s%d_%d" % (leg, p, i) for i in (1, 2, 3))
        B.block("Phase %d leg %s decoupling + RC damper" % (p, leg),
                "%d x FCSA3DS225 at the %s pins: commutation loop <= %.0f nH, bank <= %.0f nH from the leg (LAYOUT, leg deck).\n"
                "Damper (PVR-02): %d x (%d x %s CRCW2512-HP) + %d x %s 2 kV C0G in series, loop at the pins <= 3 nH."
                % (DEC_N, "/".join((top, bot)), (pvcell.LEG["Ldc"] + pvcell.LEG["Lloop"]) * 1e9, pvcell.L_BUS_REQ * 1e9,
                   DAMP_SER, DAMP_PAR, gdrv.ohm(DAMP_R), DAMP_C[1], gdrv.farad(DAMP_C[0])))
        for _ in range(DEC_N):
            B.part("FILM2U2", {"1": bus, "2": "BUS-"})
        B.C(gdrv.farad(DAMP_C[0]), bus, d1, pkg="2220", volt="2000V", diel="C0G", tol="5%")
        B.C(gdrv.farad(DAMP_C[0]), d1, d2, pkg="2220", volt="2000V", diel="C0G", tol="5%")
        for n1, n2 in ((d2, d3), (d3, "BUS-")):
            for _ in range(DAMP_PAR):
                B.part("R_DAMP", {"1": n1, "2": n2}, value=gdrv.ohm(DAMP_R))
    na, nb, n_ph = bank_n(st["n_ph"], "A", p), bank_n(st["n_ph"], "B", p), st["n_ph"]
    B.block("Phase %d share of the port banks" % p,
            "%d x FCSA3DS456 (45 uF) on A_BUS+ and %d on B_BUS+, at this phase's legs: the banks of all phases form the\n"
            "port A / port B DC links (%d / %d x 45 uF)%s. Bleeders: one string per port on the port sheets."
            % (na, nb, bank_total(n_ph, "A"), bank_total(n_ph, "B"),
               ";\nthe third on B_BUS+ is the battery side's seventh (D-056: full-power load rejection)" if nb > BANK_N else ""))
    for bus, k in (("A_BUS+", na), ("B_BUS+", nb)):
        for _ in range(k):
            B.part("FILM45", {"1": bus, "2": "BUS-"})
    B.block("Phase %d inductor (chassis, CUSTOM) and current sensor" % p,
            "Lead A from SW_A%d passes the STK-HO/A 75 U-primary (pins 6-9 in, 10-13 out: + = SW_A -> SW_B) to stud\n"
            "L_A%d; lead B on stud SW_B%d. IL%d = 2.5 V + 10.667 mV/A (Vref 2.48-2.52 V), 0.5-4.5 V over +/-187.5 A;\n"
            "100R + 1 nF at the source. IL%dR = the sensor's own Uref (pin 4), 100R + 1 nF: PV-CTL references its trip\n"
            "window to it. Primary at the switch node: functional barrier (4 kV rms, 8 kV impulse)." % (p, p, p, p, p))
    st["iso"].add(B.part("L_PV", {"1": la, "2": sb, "3": "NTC%d" % (4 + p), "4": "AGND", "5": "PE"}, value=MAG_ROW).ref)
    B.part("STUD", {"1": la})
    B.part("STUD", {"1": sb})
    B.part("STK75", dict({str(k): sa for k in range(6, 10)}, **{str(k): la for k in range(10, 14)},
                          **{"1": "+5V", "2": "AGND", "3": "IL%d_S" % p, "4": "IL%dR_S" % p, "5": None}))
    B.C("100n", "+5V", "AGND")
    for n in ("IL%d" % p, "IL%dR" % p):
        B.R("100R", n + "_S", n)
        B.C("1n", n, "AGND", diel="C0G", tol="5%")
    B.block("Phase %d NTC inputs (NTC to AGND, biased on the control board)" % p,
            "NTC%d = heatsink section of phase %d: lug probe on the EARTHED heatsink, >= 2.5 kV rms lead-to-lug (R-10).\n"
            "NTC%d = inductor winding NTC (functional to the winding). 100 nF at the header against switch-node noise."
            % (p, p, 4 + p))
    st["iso"].add(B.part("NTC_HS", {"1": "NTC%d" % p, "2": "AGND", "3": "PE"}, value="NTC 10k lug probe (CUSTOM)").ref)
    B.flag("PE")
    for n in ("NTC%d" % p, "NTC%d" % (4 + p)):
        B.part("J_NTC2", {"1": n, "2": "AGND"})
        B.C("100n", n, "AGND")
    chans =[(tag(p, s), "VDD_" + tag(p, s), "COM_" + tag(p, s), "VEE_" + tag(p, s)) for s in ("S1", "S2", "S3", "S4")]
    xf, sec = gdrv.bias_phase(B, "PH%d" % p, chans, gate_v=GATE_V, v5=v5_of(p), gnd="GND", bias_en=en_of(p))
    st["iso"] |= set(xf)
    for t, nets in sec.items():
        st["gd"].update({n: "GD_" + t for n in nets})


def sheet_drive(B, p, leg, st):
    """Phase p, one leg: two gdrv.channel() rev 7 with bias="ext" (rails from the phase's bias_phase)."""
    pair = ("S1", "S2") if leg == "A" else ("S3", "S4")
    B.new_sheet("%02d_ph%d_gd%s" % (3 + 3 * (p - 1) + (leg == "B"), p, leg.lower()),
                "Phase %d leg %s gate drive (%s, %s)" % ((p, leg) + pair),
                "gdrv.channel() rev 7, bias='ext': NSI6651ASC-Q1 +%g/-%g V, %g/%g ohm per device,\n"
                "Miller clamps, SC booster %gR, interlock + dead-time stretch, DESAT to the drain"
                % (GATE_V + R_GATE + (R_SB,)))
    for s in pair:
        drain, _, other = pos(p, s)
        t = tag(p, s)
        ch = gdrv.channel(B, t, pwm=pwm(p, int(s[1])) + "_5V", en="EN5", flt_n="FLT_N", rdy="RDY",
                          gate=tuple("G_%s%s" % (t, d) for d in "ab"[:N_PAR]),
                          source=tuple("KS_%s%s" % (t, d) for d in "ab"[:N_PAR]), drain=drain, vdd="VDD_" + t,
                          vee="VEE_" + t, interlock=pwm(p, int(other[1])) + "_5V", vin="+24V", vcc="+5V", gnd="GND",
                          gate_v=GATE_V, r_on=R_GATE[0], r_off=R_GATE[1], vclass=VCLASS, r_sb=R_SB, v_peak=V_PEAK,
                          deadtime=DT, bias="ext", neg_det=NEG_DET)
        st["gd"].update({n: "GD_" + t for n in ch.sec})
        st["iso"] |= set(ch.iso)
        st["xing"] |= set(ch.xing)
    ms = gdrv.MILLER_SIM["%d x %s" % (N_PAR, "SG2M040170HJ")]
    B.block("Leg %s: layout rules" % leg,
            "Gate and Kelvin of each device as coupled pairs of equal length (+/-10 %%) from the COM star; Ron, Roff, Kelvin\n"
            "R, 10k, Zeners at each device. Clamp FET + C_VL at its device's gate-Kelvin pins, loop <= %.0f nH. DESAT string\n"
            ">= 2.5 mm pad gap per diode; board coated to PD1 (IC-22). Miller hold (ngspice, gdrv): die %+.2f V vs VGS(th)\n"
            "min %.2f V at 175 C - BENCH TEST. Driver input side and bias primary decoupled to GND locally (CM current)."
            % (gdrv.L_CLAMP_MAX * 1e9, ms["die_l1"], gdrv.SC40["vth175"]))


def sup_window():
    """TPS3710 (SBVS271A p5: VIT- 387-400 mV, VIT+ 396-404 mV) on +5V through SUP_DIV, 0.1 %: (fall, rise) ranges."""
    r1, r2 = SUP_DIV
    k = lambda lo: (1 + r1 * (0.999 if lo else 1.001) / (r2 * (1.001 if lo else 0.999)))
    vf, vr = pvcell.TPS37["vit_f"], pvcell.TPS37["vit_r"]
    return (vf[0] * k(True), vf[1] * k(False)), (vr[0] * k(True), vr[1] * k(False))


def pending(B):
    """Guard: a PC net that no block drives gets a test point and is listed in the design check as PENDING (none today)."""
    nets = B.D.nets()
    todo = sorted(n for n, nodes in nets.items() if len([x for x in nodes if not x[0].startswith("#")]) == 1
                  and n in set(IF.PC) | set(PC_RENAME.values()))
    for n in todo:
        B.TP(n)
    return todo


# ------------------------------------------------------------------------------------------------ domains, ranges
def vranges(n_ph):
    """DC range of every assessed net against its own domain's reference (LIVE: BUS-; gate island: its COM star; PE: PE).
    gdrv.net_ranges() per channel (its logic side moved to +5V), the bias regulator nodes, then this board's nets; the
    port sheets fall back to port.vrange_lean(). Switching / gate / pulse nets stay unranged (design_check covers them)."""
    r = {}
    e = gdrv.ext_bias_numbers(GATE_V)
    for p in range(1, n_ph + 1):
        for s in ("S1", "S2", "S3", "S4"):
            t = tag(p, s)
            r.update(gdrv.net_ranges(t, GATE_V, "VDD_" + t, "VEE_" + t, tuple("KS_%s%s" % (t, d) for d in "ab"[:N_PAR]),
                                     gnd="GND", vcc="+5V", vin="+24V"))
            r.update({"%s_%s" % (x, t): (0.0, V5[1]) for x in ("DTS", "DTB", "PG")})
            b = lambda x: "%s_PH%d%s" % (x, p, t)
            r[b("RAW")] = (-e["v3"][1] + e["raw"][0], -e["v3"][0] + e["raw"][1])
            r.update({b(x): (-e["v3"][1] + gdrv.VREF431[0], -e["v3"][0] + gdrv.VREF431[1]) for x in ("RREF", "CREF")})
    r.update({"+24V": (V24[0], S75["nets"]["LIVE"][1]), "+5V": V5, "+5V_GD": V5, "+3V3": V33, "GND": (0.0, 0.0),
              "AGND": (0.0, 0.0), "BUS-": (0.0, 0.0), "PE": (0.0, 0.0), "SUP5_SNS": (0.0, V5[1] * SUP_DIV[1] / sum(SUP_DIV)), "A_BUS+": (0.0, port.V_POLE),
              "SUP5G_SNS": (0.0, V5[1] * SUP_DIV[1] / sum(SUP_DIV)), "FB_5V": (0.985, 1.015), "FB_5VG": (0.985, 1.015),
              "PG_5V": (0.0, V5[1]), "PG_5VG": (0.0, V5[1]), "RT_5V": (0.0, 1.5), "RT_5VG": (0.0, 1.5),
              "FB_3V3": (0.78, 0.83), "SS_3V3": (0.0, 1.3), "DIS_G": (0.0, 10.4),
              "B_BUS+": (0.0, port.V_POLE)})
    r.update({n: (0.0, V33[1]) for n in ["EN", "BIAS_EN", "RDY", "FLT_N", "HOLD", "MOV_OK", "K_A", "K_B", "K_PRE", "IMD_SW1",
                                         "IMD_SW2"] + ["PWM%d" % k for k in range(1, 17)] + ["NTC%d" % k for k in range(1, 9)]})
    r.update({n: (0.0, V5[1]) for n in ["EN5", "BIAS_EN5", "BIAS_EN5G"] + ["PWM%d_5V" % k for k in range(1, 17)]
              + ["IL%d" % k for k in range(1, 5)] + ["IL%dR" % k for k in range(1, 5)]})
    return r


def build_design(n_ph):
    B = L.Builder(PROJECT[n_ph], "%s power board" % PROJECT[n_ph], REV, DATE, CATALOG, rails=["+24V", "+5V", "+3V3"],
                  returns=["GND", "AGND", "PE"],
                  subtitle="%s: %d interleaved FSBB phases, gate drive, sensing, ports, aux (D-044)"
                           % ("PV-P75" if n_ph == 3 else "PV-P100/110", n_ph),
                  comment1="Live board referenced to BUS-; gate islands functional; SELV winding reinforced; HV-PE basic",
                  comment4="Not bench-validated. Values read from sim/out/*.json; checks: design_check()")
    st = dict(gd={}, iso=set(), xing=set(), dom={"PE_T": "PE", "PE_D": "PE"}, n_ph=n_ph)
    sheet_pc(B, n_ph)
    for p in range(1, n_ph + 1):
        sheet_power(B, p, st)
        sheet_drive(B, p, "A", st)
        sheet_drive(B, p, "B", st)
    sheets_ports(B, n_ph, st)
    sheets_supplies(B, n_ph, st)
    st["todo"] = pending(B)
    return B, st


def pin_numbers(entry):
    if "stock" in entry:
        import symlib
        return {q.number for q in symlib.symbol_pins(symlib.kicad_symbol(entry["stock"][0], entry["stock"][1], "x"))}
    return {x.split()[0] for u in (entry.get("units") or [entry["pins"]]) for side in u.values() if isinstance(side, list)
            for x in side if x}


def sheets_supplies(B, n_ph, st, no=None, taps=("A_IN+", "B_T+", "BUS-"), gd_what=None):
    """Live rails from the aux block's live 24 V: +5V and +5V_GD (LMR38020, 2 A each), +3V3 (TPS62130 from +5V_GD with a
    controlled ramp-up and a discharge stage), the +5V_GD supervisor and the SELV connector; then gen/aux_hv.py
    aux75_block (4 sheets) through aux_block()."""
    no = 2 + 3 * n_ph + 5 if no is None else no
    B.new_sheet("%02d_supplies" % no, "Live 5 V / 3.3 V, SELV connector",
                "+24V (aux live) -> +5V and +5V_GD (LMR38020), +3V3 (TPS62130 from +5V_GD,\n"
                "ramp-up and discharge), +5V_GD supervisor, SELV connector to the control board")
    for rail, t, what in (("+5V", "5V", "NSI6651 inputs, AHCT, sensors, references, PC +5V, gate bias of phases 1-2"),
                          ("+5V_GD", "5VG", gd_what or "gate bias of phases 3%s" % ("-4" if n_ph == 4 else " only"))):
        B.block("24 V -> %s (LMR38020, 400 kHz, 2 A)" % rail,
                "%s. ctrl_c2000 circuit (SNVSC40E table 9-1, 400 kHz / 5 V / 2 A): 15 uH, 3 x 22 uF, RT 64.9k,\n"
                "FB 100k / 24.9k 0.1 %% -> %.2f-%.2f V. Load in design_check (<= 80 %% of 2 A)." % (what, V5[0], V5[1]))
        B.part("LMR38020", {"3": "+24V", "2": "+24V", "4": "RT_" + t, "8": "SW_" + t, "7": "BOOT_" + t, "5": "FB_" + t,
                            "6": "PG_" + t, "1": "GND", "9": "GND"})
        B.C("4.7u", "+24V", "GND", pkg="1210", volt="50V")
        B.C("4.7u", "+24V", "GND", pkg="1210", volt="50V")
        B.C("100n", "+24V", "GND", volt="100V")
        B.R("64.9k", "RT_" + t, "GND")
        B.C("100n", "BOOT_" + t, "SW_" + t)
        B.part("L15U", {"1": "SW_" + t, "2": rail})
        for _ in range(3):
            B.C("22u", rail, "GND", pkg="1206", volt="16V", tol="10%")
        B.R(gdrv.ohm(FB5[0]), rail, "FB_" + t, tol="0.1%")
        B.R(gdrv.ohm(FB5[1]), "FB_" + t, "GND", tol="0.1%")
        B.R("100k", rail, "PG_" + t)
        B.TP("PG_" + t)
        B.flag(rail)
    B.block("+5V_GD supervisor on RDY", "TPS3710 %s/%s as on +5V: RDY low while the bias rail of phases 3%s is below "
            "4.52-4.69 V." % (gdrv.ohm(SUP_DIV[0]), gdrv.ohm(SUP_DIV[1]), "-4" if n_ph == 4 else ""))
    B.part("TPS3710", {"5": "+5V_GD", "3": "SUP5G_SNS", "1": "RDY", "2": "GND", "4": "GND", "6": "GND"})
    B.C("100n", "+5V_GD", "GND")
    B.R(gdrv.ohm(SUP_DIV[0]), "+5V_GD", "SUP5G_SNS", tol="0.1%")
    B.R(gdrv.ohm(SUP_DIV[1]), "SUP5G_SNS", "GND", tol="0.1%")
    B.C("1n", "SUP5G_SNS", "GND")
    B.block("+5V_GD -> +3V3 (TPS62130, 2.5 MHz) with a controlled ramp",
            "EN = PG_5VG. FB %s / %s 0.1 %% -> %.3f-%.3f V (>= 3.20 V for the control board's reference). SS/TR %s C0G:\n"
            "ramp-up 12-16 mV/us (F28003x VDDIO 8-100 mV/us). Ports' logic, RDY / MOV_OK pull-ups, PC +3V3 (control <= 157 mA)."
            % (gdrv.ohm(FB33[0]), gdrv.ohm(FB33[1]), V33[0], V33[1], gdrv.farad(SS33)))
    B.part("TPS62130", {"11": "+5V_GD", "12": "+5V_GD", "10": "+5V_GD", "13": "PG_5VG", "9": "SS_3V3", "7": "GND",
                        "8": "GND", "1": "SW_3V3", "2": "SW_3V3", "3": "SW_3V3", "14": "+3V3", "5": "FB_3V3", "4": None,
                        "6": "GND", "15": "GND", "16": "GND", "17": "GND"})
    B.C("10u", "+5V_GD", "GND", pkg="1210", volt="25V")
    B.C("100n", "+5V_GD", "GND")
    B.C(gdrv.farad(SS33), "SS_3V3", "GND", diel="C0G", tol="5%")
    B.part("L2U2", {"1": "SW_3V3", "2": "+3V3"})
    B.C("22u", "+3V3", "GND", pkg="0805", volt="10V", tol="10%")
    B.C("22u", "+3V3", "GND", pkg="0805", volt="10V", tol="10%")
    B.R(gdrv.ohm(FB33[0]), "+3V3", "FB_3V3", tol="0.1%")
    B.R(gdrv.ohm(FB33[1]), "FB_3V3", "GND", tol="0.1%")
    B.block("+3V3 discharge (ramp-down when the rails fail)",
            "PG_5VG low (+5V_GD < 90-94 %%, i.e. the live 24 V is gone) disables the TPS62130 and lets the 100k from +24V\n"
            "(10 V Zener) turn on PMV30ENEA + %s: +3V3 falls at >= 20 mV/us through the BOR region (F28003x SRVDDIO-DN)."
            % gdrv.ohm(R_DIS33))
    B.part("AO3400A", {"1": "DIS_G", "2": "GND", "3": "DIS_D"})
    B.R(gdrv.ohm(R_DIS33), "+3V3", "DIS_D", pkg="2512", note="+3V3 discharge, pulse 0.5 mJ")
    B.R("100k", "+24V", "DIS_G", note="discharge on unless PG_5VG holds it off")
    B.part("BZX84-B10", {"1": "GND", "2": None, "3": "DIS_G"})
    B.part("2N7002BK", {"1": "PG_5VG", "2": "GND", "3": "DIS_G"})
    B.block("SELV 24 V to the control board (J2)", "AUX-T1 reinforced winding SELV_24V / SELV_0V, cross-regulated %.1f-%.1f V "
            "(aux75_spec); full fan speed needs\n%.1f V. %s. Fan buck (12-36 V in) + SELV logic on the control board;\n"
            ">= 10 mm from live copper; nothing else of the SELV domain is on this board."
            % (S75["regulation"]["selv_V_all"][0], S75["regulation"]["selv_V_all"][1],
               S75["regulation"]["fan_full_speed_needs_V"], FAN_RULE))
    B.part("J_SELV", {"1": "SELV_24V", "2": "SELV_0V"})
    st["aux"] = aux_block(B, no + 1, taps)
    st["iso"] |= set(st["aux"]["isolators"])
    st["selv"] = set(st["aux"]["selv_nets"])


FAN_RULE = "Full fan speed is only guaranteed while the converter is switching"
AUX_SWAP = {}    # catalogue keys defined by this board AND aux_hv with a different entry: {key: (board MPN, aux MPN)}


def aux_block(B, sheet_no, taps=("A_IN+", "B_T+", "BUS-")):
    """gen/aux_hv.py aux75_block(). Keys that both catalogues define (aux_hv vs gdrv / port / pvcell, e.g. 'BAT54' =
    'BAT54' here and 'BAT54,215' there - the same Nexperia part with its packing suffix) are swapped to the aux entry for
    the call only, so the aux block's own MPN self-check holds, then restored. Checked: equal pin numbers, every shared
    key maps to the same MPN before and after the call, and every part drawn under a shared key carries exactly the
    board MPN (board parts) or the aux MPN (aux parts) - a silent part change cannot pass."""
    shared = sorted(k for k in S75["parts"] if k in B.catalog)
    before = {k: B.catalog[k]["mpn"] for k in shared}
    swap = {k: B.catalog[k] for k in shared if B.catalog[k] != aux_hv.CATALOG[k]}
    for k in swap:
        assert pin_numbers(swap[k]) == pin_numbers(aux_hv.CATALOG[k]), "catalogue key %s: aux and board symbols differ" % k
        B.catalog[k] = aux_hv.CATALOG[k]
    try:
        aux = aux_hv.aux75_block(B, a_tap=taps[0], b_tap=taps[1], bus_n=taps[2], live="+24V", selv_p="SELV_24V",
                                 selv_n="SELV_0V", status="RDY", prefix="AUX_", sheet_no=sheet_no)
    finally:
        B.catalog.update(swap)
    assert {k: B.catalog[k]["mpn"] for k in shared} == before, "a shared catalogue key changed its MPN across the aux call"
    mine = set(aux["refs"])
    for ref, p_ in B.D.parts.items():
        k = p_.lib_id.split(":")[1]
        if k in before:
            want = aux_hv.CATALOG[k]["mpn"] if ref in mine else before[k]
            assert B.bom[ref]["mpn"] == want, "%s (key %s) drawn as %s, expected %s" % (ref, k, B.bom[ref]["mpn"], want)
    AUX_SWAP.update({k: (before[k], aux_hv.CATALOG[k]["mpn"]) for k in swap})
    return aux


def domain_for(st):
    return lambda net: st["gd"].get(net) or st["dom"].get(net) or ("PE" if net == "PE" else "SELV" if
                                                                   net in st["selv"] else "LIVE")


# ------------------------------------------------------------------------------------------------ design check
# Datasheet values used below (document, page). "ASSUMED" marks a value that is not a datasheet or spec number.
STK = dict(ipn=75.0, ipm=187.5, g=10.667e-3, vref=(2.48, 2.52), voe=10e-3, voe_t=0.015, vfs=0.8, lin=0.005, x_t=0.03,
           t_res=0.2e-6, bw=1e6, icc=9e-3, vcc=(4.75, 5.25), noise_pp=25e-3, r_out=(15.0, 25.0), r_ref=(12.0, 20.0),
           ud=4000.0, uw=8000.0, creep=13.78)
#   Sinomags STK-HO/A Ver1.5 p5 (STK-HO/A 75): IPN 75 A, IPM +/-187.5 A, Vcc 4.75-5.25 V, Icc <= 9 mA, Vref 2.48-2.52 V,
#   V_FS 0.8 V at IPN, R_out 15-25 ohm, R_ref 12-20 ohm (Uref output), Voe +/-10 mV (Vout - Vref at 0 A),
#   Voe drift +/-1.5 % V_FS, G_th 10.667 mV/A, linearity +/-0.5 % IPN,
#   t_res 0.2 us, BW 1 MHz, noise 25 mVpp (DC-100 kHz), accuracy +/-3 % IPN -40..105 C; p3: 4 kV rms, 8 kV 1.2/50 us,
#   creepage = clearance 13.78 mm. STK-HO/A 130 (architecture's pick, p7): IPN 130 A, 6.154 mV/A, linearity 0.7 % IPN.
STK130 = dict(ipn=130.0, g=6.154e-3, lin=0.007)
F45 = dict(c=45e-6, v85=1100.0, v70=1300.0, irms85=22.1, ipk=900.0, esl=35e-9, esr=4.0e-3)   # Jianghai CBB138 DS p30
F22 = dict(c=2.2e-6, v85=1100.0, v70=1300.0, irms85=3.9, ipk=176.0, esl=25e-9, esr=22.5e-3, rth=33.0)   # p30 row 2.2 uF
VY1_VDC = 1500.0                                   # Vishay VY1 p1: Y1 500 VAC / 1500 VDC
IQ = dict(opa2388=2.6e-3, tlv3502=5e-3, ref3030=37e-6, lvc=10e-6, ahct=10e-6, ahct_d=1.5e-3, sn6505=2.3e-3)
#   OPA4388 SBOS777D IQ <= 2.6 mA per amplifier; TLV3502 SBOS321E IQ <= 5 mA (pvcell TLV); REF3030 <= 37 uA; LVC ICC
#   <= 10 uA; SN74AHCT1G08 SCLS315S ICC <= 10 uA + dICC <= 1.5 mA per input at 3.4 V; SN6505B SLLSEP9I I(VCC) <= 2.3 mA
COIL = dict(hfe82v=6.0, g7l=2.3)                   # W at 24 V: Hongfa HFE82V-300C p1 (no economiser); Omron G7L-X p2 DC24
NSI = gdrv.NSI
NSI_TYP = dict(icc1=1.6e-3, icc2=3.3e-3)           # NSI66x1A-Q1 p.6: ICC1 0.6 / 1.6 / 4 mA, ICC2 1 / 3.3 / 7 mA (min / typ / max)
T_IN, T_BOARD, ETA_5V = 45.0, pvcell.T_BOARD, 0.85   # inlet (PV-11/PV-20 rating point); board 85 C, 5 V buck ASSUMED
ETA_33 = 0.85                                      # TPS62130 5 -> 3.3 V at 0.1-0.4 A: ASSUMED (SLVSAG7F curves ~0.88-0.92)
R_SA = {3: 0.06, 4: 0.049}                         # K/W heatsink target incl. air rise (ARCHITECTURE section 9)
CTL_C33, CTL_C33A = (11.0e-6, 2.9e-6), 2.5e-6     # PV-CTL rev A0 netlist: +3V3 = 10u + 1u (large) + 29 x 100n; +3V3A 2.5 uF
CTL_IL_LOAD = 39.4e3                              # PV-CTL rev A1: load of each IL line (its x 0.7462 divider)
CTL_ILR_LOAD = 39.8e3                             # PV-CTL rev A1: load of each ILnR line (715R + 19.1k + 20.0k trip ladder)
CTRL_LOAD = {"+3V3": 0.20, "+5V": 0.0, "+24V": 0.0}   # A allocated to the control board (PV-CTL rev A0 draws <= 0.157 A on
#                                                    +3V3 and nothing from +5V / +24V)
ECON = port.S["lean"]["coil_economiser"]           # gen/port.py lean_contactor economiser (default on): hold / pull-in
SELV_LOGIC_W = 2.2                                 # control board SELV zone, allocation (D-075): PV-CTL 1.44 W stacked maximum with the
#                                                    Ethernet bridge not fitted, 2.13 W fitted (PCS-CTL); the aux block allocates the same 2.2 W
SELV_W = {3: 39.6 + SELV_LOGIC_W, 4: 56.1 + SELV_LOGIC_W}   # ARCHITECTURE section 3: fans at full speed (+10 % buck) + SELV logic
LABEL_MIN = {3: 10.0, 4: 15.0}                     # ARCHITECTURE 2.2 (4): enclosure label 'wait 10 / 15 min'


def aux_rating(n_ph):
    """The aux block's ratings for this variant (aux75_spec 'ratings': live_W, live_peak_W, selv_W, total_W)."""
    return next(v for k, v in S75["ratings"].items() if k.startswith("%d phases" % n_ph))


def selv_rows(n_ph):
    """aux75_spec selv_table_V: [(live 24 V load W, SELV minimum V)] with the fans at 100 %, for this build"""
    return sorted((float(re.search(r"live ([\d.]+) W", k).group(1)), v[0]) for k, v in S75["regulation"]["selv_table_V"].items()
                  if k.startswith("%d phases" % n_ph) and k.endswith("fans 100 %"))


def live_min_for_fans(n_ph):
    """Live 24 V load above which the SELV winding stays >= fan_full_speed_needs_V with the fans at 100 % (aux75_spec
    selv_table_V minima, linear between its live-load rows)."""
    need = S75["regulation"]["fan_full_speed_needs_V"]
    rows = selv_rows(n_ph)
    for (w1, v1), (w2, v2) in zip(rows, rows[1:]):
        if v1 < need <= v2:
            return w1 + (need - v1) * (w2 - w1) / (v2 - v1)
    return rows[0][0] if rows[0][1] >= need else float("inf")


def selv_min_at(n_ph, live_w):
    """SELV minimum (V) at a live 24 V load with the fans at 100 %: aux75_spec selv_table_V, linear between its rows"""
    rows = selv_rows(n_ph)
    return float(np.interp(live_w, [w for w, _ in rows], [v for _, v in rows]))


def fan_contract(n_ph):
    """PCM-26 - ONE contract for the fan supply. S_24V at the worst cross-regulation point (aux75_spec: fans at 100 %, the live load at
    which the SELV winding first guarantees fan_full_speed_needs_V), what the fan buck then passes (gen/pv_ctrl.py fan_ceiling: the
    TPS54360B in dropout with the drawn choke and catch diode, at the fans' current), the voltage the thermal model's fans run at
    (module_spec fan_speed_cap x 24 V) and the airflow ratio that follows (speed ~ voltage ASSUMED, as sim/pv_module.py). gen/pv_ctrl.py
    re-derives it from its own drawn parts and compares with the line this board prints"""
    import pv_ctrl as CTL
    var = "PV-P75" if n_ph == 3 else "PV-P100/110"
    m = MODS["modules"][var]
    s_min = S75["regulation"]["fan_full_speed_needs_V"]
    v_need = CTL.FAN_V_RATED * m["fan_speed_cap"]
    i = CTL.FAN_W[var] / v_need
    v_pass = CTL.fan_ceiling(s_min, i)
    ratio = min(1.0, v_pass / v_need)
    if ratio < 1.0 - FAN_FLOW_TOL:
        raise SystemExit("%s: the fan supply passes only %.2f V of the %.2f V the thermal model's fans run at (airflow x%.3f < x%.3f): "
                         "derate module_spec airflow and the heatsink temperature (sim/pv_module.py)" %
                         (var, v_pass, v_need, ratio, 1.0 - FAN_FLOW_TOL))
    return dict(var=var, s_min=s_min, v_need=v_need, i=i, v_pass=v_pass, ratio=ratio, flow_min=1.0 - FAN_FLOW_TOL,
                q0=m["airflow_m3h_full_45C"], exp=MODS["costfirst"]["heatsink"]["R_sa_flow_exponent"][var],
                v_rated=CTL.FAN_V_RATED, d=CTL.FAN_BUCK["d"], rds=CTL.FAN_BUCK["rds"], rdc=CTL.fan_r_dc(),
                vin_full=CTL.fan_vin_for(CTL.FAN_V_RATED, i))


def port_assumption(name):
    """one of the port design's assumptions (the table 'A_*' of sim/out/port_design/report.md); a missing one stops the build"""
    m = re.search(r"^\| %s \| ([0-9.e+-]+) \|" % name, open(OUT("port_design", "report.md")).read(), re.M)
    if not m:
        raise SystemExit("%s not found in sim/out/port_design/report.md: regenerate it with .venv/bin/python sim/port_design.py" % name)
    return float(m.group(1))


def rlc_peak(v, r, l, c):
    """peak current (A) of a series R-L-C closing onto an uncharged capacitor c from a stiff source v (the closed form of the port design)"""
    a, w0 = r / (2 * l), 1 / math.sqrt(l * c)
    if a < w0:                                   # under-damped: i = v / (wd l) e^(-a t) sin(wd t), peak where tan(wd t) = wd / a
        wd = math.sqrt(w0 * w0 - a * a)
        t = math.atan(wd / a) / wd
        return v / (wd * l) * math.exp(-a * t) * math.sin(wd * t)
    w = math.sqrt(max(a * a - w0 * w0, 1e-12))   # over-damped: i = v / (2 w l) (e^((-a + w) t) - e^((-a - w) t))
    t = math.log((a + w) / (a - w)) / (2 * w)
    return v / (2 * w * l) * (math.exp((-a + w) * t) - math.exp((-a - w) * t))


def port_a_declaration(n_ph):
    """PCM-16: what port A tolerates, from the drawn hardware (port_spec lean, the port design's assumptions): the admissible source type,
    external fusing, connection sequence, source capacitance and reverse-power permission, as one block of the design check. No hardware."""
    rating = {3: 135, 4: 180}[n_ph]
    ln = port.S["lean"]
    pv, ct, mk, hold = ln["pv_port"][str(rating)], ln["contactors"]["HFE82V"], ln["pv_make"][str(rating)], ln["contactor"]
    v_max = 1000.0
    c_a = bank_total(n_ph, "A") * F45["c"] + DEC_N * n_ph * F22["c"]                  # the bank behind K_A
    esr = F45["esr"] / bank_total(n_ph, "A")
    r_s, l_s = port_assumption("A_RS_BATT"), port_assumption("A_LS_BATT")             # a stiff source: 0.03 ohm, 3 uH incl. a short cable
    r_x, l_x = port_assumption("A_R_LOOP_X"), port_assumption("A_L_LOOP")             # the module's own loop to the bank
    i_stiff = rlc_peak(v_max, r_s + r_x + esr, l_s + l_x, c_a)
    i_dis, c_pe = port_assumption("A_I_MAKE_PV"), port_assumption("A_C_PV_PE" if n_ph == 3 else "A_C_PV_PE_110")
    l_arr = 10e-6 + l_x                                                               # port_design: a PV source behind 10 uH of cable
    c_src = l_arr * (i_dis / v_max) ** 2                                             # source capacitance whose discharge peaks at i_dis
    oc = ln["port_oc_trip_A"]
    return ("PORT A DECLARATION (PCM-16; calculated from port_spec lean and the port design's assumptions, ESTIMATES labelled; no hardware "
            "change). Port A admits: a current-limited PV array only - short-circuit current at the module terminals <= %.1f A (1.25 x the "
            "%d A port rating; K_A breaks %.0f A at 1000 V both polarities x %d operations: margin x%.2f, carries x%.2f), open-circuit "
            "voltage <= %.0f V (OV trip band 1039-1110 V), connected to the DC terminals through string fuses in the combiner (IEC 62548, "
            "ARCHITECTURE-COSTFIRST 6.3) and a load-break isolator, array and cable capacitance terminal to terminal <= %.1f uF behind "
            ">= %.0f uH (the 330 A discharge peak the making estimate assumes, back-calculated: ESTIMATE; the array's capacitance to PE "
            "is %.1f uF, common mode only); connection: K_A closes only with the latch clear, VAX above the polarity enable (%d-%d V "
            "band: a reversed array cannot be closed onto), the IMD result in range and, with port B live, after the converter has "
            "pre-charged the %.0f uF A bank to within 20 V (then the making current is the array's Isc), otherwise onto the EMPTY bank "
            "at the array's Voc: making current about %.0f A (Isc %.0f A + %.0f A discharge, ESTIMATE) against a published making "
            "rating of %.0f A at %.0f V only - covered: %s (Hongfa to confirm, R-04). Reverse power B -> A is NOT admitted with an "
            "array: there is no series diode, fuse or precharge on port A, the port over-current window (%d-%d A, both directions, "
            "FLT_N) protects the module and not the array, and an array driven backwards conducts through its cells and bypass diodes "
            "(limited only by the modules' reverse-current rating and the combiner's string fuses) - firmware holds the port A "
            "current at >= 0 while the port is declared PV (second layer behind the converter's own current limit). Port A does NOT "
            "admit: a stiff DC source (battery, DC bus, rectifier, another converter) - K_A would close onto the empty %.0f uF bank "
            "with a peak of about %.1f kA at %.0f V (%.2f ohm + %.1f uH source and loop, %.0f J stored: %.0fx the making rating's %.0f A, "
            "weld likely), a fault fed by it is cleared only by K_A (<= %.0f A normal opening, hold-off to %d-%d A, %.0f A once) with no "
            "fuse behind it, and nothing blocks reverse current; a stiff DC source on port A requires the PV-PORT-180 / lean port with "
            "fuse and precharge (gen/port.py lean_port as the battery port B: 2 x HPE501 250 A aR links, 220 ohm precharge, "
            "polarity and dV interlocks)" %
            (pv["isc"], rating, ct["break_1000V_both"], ct["n_break"], pv["brk_margin"], pv["carry"], v_max, c_src * 1e6, l_arr * 1e6,
             c_pe * 1e6, ln["polarity_enable_V"][0], ln["polarity_enable_V"][1], c_a * 1e6, mk["i_make_est"], pv["isc"], i_dis,
             ct["make_published"][0], ct["make_published"][1], "yes" if mk["covered"] else "NO", oc[0], oc[1], c_a * 1e6, i_stiff / 1e3,
             v_max, r_s + r_x + esr, (l_s + l_x) * 1e6, 0.5 * c_a * v_max ** 2, i_stiff / ct["make_published"][0],
             ct["make_published"][0], ct["break_1000V_both"], hold["hold_off_band_A"][0], hold["hold_off_band_A"][1],
             hold["break_once_published_A"]))


def leg_commutation():
    """PCM-18 (R-08 closed): the leg commutation with the capacitors AS DRAWN - cell_spec leg_commutation (sim/pv_design.py: the Jianghai
    FCSA3DS456 bank share and the FCSA3DS225 leg decoupling in the ngspice leg deck, at 1000 V / 1100 V and at the normal peak / the
    hardware-trip current) and the gate-source excursion of the held-off device at the same corners (sim/gdrv_miller.py). Returns the
    result text; the limits are asserted, a missing or stale record stops the build"""
    cd, lc, dc = spec("capacitors_drawn"), spec("leg_commutation"), spec("decoupling")
    for blk, f in ((cd["bank"], F45), (cd["decoupling"], F22)):        # the deck's capacitor data = the parts drawn here
        for k_cd, k_f in (("C", "c"), ("vop85", "v85"), ("vndc", "v70"), ("irms85", "irms85"), ("ipkr", "ipk"), ("esl", "esl"), ("esr", "esr")):
            assert abs(blk[k_cd] / f[k_f] - 1) < 1e-9, "cell_spec capacitors_drawn %s differs from the part drawn here (%s): re-run sim/pv_design.py" % (k_cd, k_f)
    assert cd["bank"]["count_per_phase_and_port"] == BANK_N and cd["decoupling"]["count_per_leg"] == DEC_N == dc["count_per_leg"], \
        "cell_spec capacitors_drawn counts differ from the drawing: re-run sim/pv_design.py"
    path = OUT("gdrv_miller", "result_primary.json")
    if not os.path.exists(path):
        raise SystemExit("%s is missing: generate it with .venv/bin/python sim/gdrv_miller.py" % os.path.relpath(path, L.REPO))
    gm = json.load(open(path))["primary"]
    if "corners" not in gm or gm["dev"] != "SG2M040170HJ":
        raise SystemExit("%s has no corner runs of the SG2M040170HJ: re-run sim/gdrv_miller.py" % os.path.relpath(path, L.REPO))
    near = lambda r, v, i: abs(r["V"] - v) < 1e-6 and abs(r["I_A"] - i) < 0.06
    worst_run = next(r for r in gm["runs"] if abs(r["l_clamp_nH"] - 1.0) < 1e-9)      # 1100 V at the hardware-trip current, 1 nH loop
    gs = []
    for c in lc["corners"]:
        if c["V"] == lc["corners"][-1]["V"] and c["case"] == "hardware trip":          # the worst-device corner = the miller study's own run
            gs.append((worst_run["nfet"]["pin_pk"], worst_run["nfet"]["die_pk"], worst_run["v_pk"]))
            continue
        m = [r for r in gm["corners"] if near(r, c["V"], c["I_A"])]
        if len(m) != 1:
            raise SystemExit("%s has no run at %.0f V / %.1f A (cell_spec leg_commutation corner): re-run sim/gdrv_miller.py" %
                             (os.path.relpath(path, L.REPO), c["V"], c["I_A"]))
        gs.append((m[0]["pin_pk"], m[0]["die_pk"], m[0]["device_peak_V"]))
    for c, g in zip(lc["corners"], gs):                                                 # the same leg deck behind both files
        assert abs(c["device_peak_V"] - g[2]) < 1.0, "gdrv_miller and cell_spec leg decks disagree (stale): re-run sim/pv_design.py and sim/gdrv_miller.py"
    v_lim, vth = lc["device_peak_limit_V"], gm["vth_175_min"]
    die_max = max(g[1] for g in gs)
    assert max(c["device_peak_V"] for c in lc["corners"]) <= v_lim, "leg commutation: device peak above 0.85 x V_DSS"
    assert die_max <= vth - 0.5 + 1e-9, "held-off device: gate-source excursion above V_GS(th) min less the 0.5 V design margin"
    net, cs = lc["network"], lc["corners"]
    return ("Leg commutation with the capacitors AS DRAWN (PCM-18, R-08 closed; cell_spec leg_commutation, ngspice VDMOS decks "
            "sim/spice/pv_dpt_leg_c*.cir, calculated): bank share %d x FCSA3DS456 per phase (%.0f nH / %.1f mOhm each, Jianghai CBB138 "
            "p.30 values, the earlier deck ran the KEMET 19 / 24 nH) -> %.0f nH bus -> %d x FCSA3DS225 (%.1f nH / %.1f mOhm per leg) -> "
            "%.1f nH board + devices -> RC damper; device V_DS peak %s against %.0f V = 0.85 x 1700 V; gate-source of the held-off "
            "device (gdrv clamp network, 1 nH loop, %.1f V bias, sim/gdrv_miller.py): pin %.2f..%.2f V, die %+.2f..%+.2f V against "
            "V_GS(th) min %.2f V at 175 C (margin %.2f V, design margin 0.5 V); decoupling capacitor current per FCSA3DS225: peak "
            "%.1f-%.1f A over the corners (%.1f A at the worst on-time, %.1f A with the Q_rr surrogate) against Ipkr %.0f A, rms "
            "%.2f-%.2f A (%.2f A at the worst on-time) against %.1f A at 85 C / %.1f A at 70 C" %
            (cd["bank"]["count_per_phase_and_port"], cd["bank"]["esl"] * 1e9, cd["bank"]["esr"] * 1e3, net["bus_nH"],
             cd["decoupling"]["count_per_leg"], net["decoupling_ESL_nH"], net["decoupling_ESR_mOhm"], net["board_and_devices_nH"],
             "; ".join("%.0f V (%.0f V / %.1f A %s)" % (c["device_peak_V"], c["V"], c["I_A"], c["case"]) for c in cs), v_lim,
             gm["runs"][0]["voff"], min(g[0] for g in gs), max(g[0] for g in gs), min(g[1] for g in gs), die_max, vth, vth - die_max,
             min(c["decoupling_peak_per_cap_A"] for c in cs), max(c["decoupling_peak_per_cap_A"] for c in cs),
             dc["peak_current_per_cap_A"], dc["peak_current_per_cap_with_recovery_A"], cd["decoupling"]["ipkr"],
             min(c["decoupling_rms_per_cap_A"] for c in cs), max(c["decoupling_rms_per_cap_A"] for c in cs), dc["rms_per_cap_A"],
             cd["decoupling"]["irms85"], cd["decoupling"]["irms"]))


def stamp():
    """the 'Built from' line of the design check: sha256 (first 16 hex) of every spec file this board's numbers were read from"""
    return "Built from (sha256, first 16 hex): " + "; ".join(
        "%s %s" % (f, hashlib.sha256(open(os.path.join(L.REPO, f), "rb").read()).hexdigest()[:16]) for f in STAMP_FILES)


def island_idle_in_w():
    """Upper bound of one island's 5 V input power with the bias on and the gates NOT switching: resistor currents at the
    highest rails (COM bias 4.7k -1 %, both dividers, VCG 10k, gate pull-downs 10k, negative-rail detector 100k) plus the
    NSI6651 ICC2 maximum, drawn through the linear regulator from the highest raw voltage, transformer 90 %."""
    e = gdrv.ext_bias_numbers(GATE_V)
    dv = gdrv.EXT_DIV[GATE_V]
    i = (e["von"][1] / (4.7e3 * 0.99) + e["vt"][1] / (sum(dv["vdd"]) * 0.999) + e["v3"][1] / (sum(dv["vee"]) * 0.999)
         + (e["von"][1] - 3.26) / (10e3 * 0.99) + N_PAR * e["v3"][1] / (10e3 * 0.99) + NSI["icc2"]
         + (e["vt"][1] / 100e3 if NEG_DET else 0.0))
    return e["raw"][1] * i / 0.9


def island_resistor_w():
    """Deterministic resistor power of one gate island at its lowest rails (COM bias 4.7k, both 0.1 % dividers, VCG
    supply 10k, gate pull-downs 10k): the floor of the bias load with the gates off."""
    e = gdrv.ext_bias_numbers(GATE_V)
    gv = gdrv.GATE_V[GATE_V]
    i = (e["von"][0] / 4.7e3 + e["vt"][0] / sum(gv["fbvdd"]) + e["v3"][0] / sum(gv["fbvee"])
         + (e["von"][0] - 3.34) / 10e3 + N_PAR * e["v3"][0] / 10e3)
    return e["vt"][0] * i


def thermal_inputs():
    """R_th chain and the per-phase device losses of the full-load table of sim/out/pv_design/report.md (cell_spec does
    not carry them): (R_jc, R_cs, R_spread, worst device loss per phase over the full-load points)."""
    txt = open(OUT("pv_design", "report.md")).read()

    def f(pat):
        m = re.search(pat, txt)
        if not m:
            raise SystemExit("sim/out/pv_design/report.md: %r not found - re-run sim/pv_design.py" % pat)
        return float(m.group(1))
    rows = re.findall(r"^\| (\d+)->(\d+) \| ([\d.]+) \| \w+ \| [\d.]+ \| [\d.]+ \| ([\d.]+) \| ([\d.]+) \| ([\d.]+) \|", txt,
                      re.M)
    if len(rows) < 8:
        raise SystemExit("sim/out/pv_design/report.md: the full-load table is not found - re-run sim/pv_design.py")
    return (f(r"R_th,jc ([\d.]+) K/W"), f(r"case-sink ([\d.]+) K/W"), f(r"spreading ([\d.]+) K/W"),
            max(float(c) + float(s_) + float(d) for *_, c, s_, d in rows))
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
