vectivolt/PCM/gen/port.py

"""DC PORT block + PV-PORT board (REQUIREMENTS.md PV-03..PV-08, PV-C3..C5, ECO-07, ECO-09, ECO-10).

One port = everything between a module's DC terminals and its internal bus: terminals, a fuse on each pole, DC SPD to
PE, X/Y + common-mode filter, bidirectional main contactor (+ pole), precharge relay + resistor, 100 uOhm shunt in the
- pole, fail-safe active discharge (inhibited while the contactor is closed, time-limited, thermal cut-off) + passive
bleeder, voltage sense on both sides of the contactor and current sense as isolated-amplifier pairs of the PORT
contract, coil drives with two switches in every coil-current path, a two-channel hold-closed interlock with a
proof-test input and readback. Every value comes from sim/port_design.py (sim/out/port_design/port_spec.json - run
it first).

Reuse (the DAB board calls it twice, for two ports isolated from each other):

    import port
    CATALOG = dict(catalog.PARTS, **port.CATALOG)      # port.PARTS + gdrv's SN74LVC1G17 (skip it if you merge gdrv)
    p1 = port.port(B, "A", "P1_BUS+", "P1_BUS-", sheet_no=2, hv="HV1")   # adds sheets 02 + 03 (135 A default)
    p2 = port.port(B, "B", "P2_BUS+", "P2_BUS-", sheet_no=4, hv="HV2")   # adds sheets 04 + 05
    # PV-P100/110 (4 cells, 180 A per port): port.port(..., rating=180) - see report sec. 6.4 / 12 for its limits
    B.part("J_CTRL", {str(i): x for i, x in enumerate(port.CTRL_PINS, 1)})   # 14-way, one harness for every board
    # route p1["nets"]["rb1"], ["rb2"] (and p2's) to CTRL on a spare line (PV-PORT: ID-line DAC in board_io())
    domain_of = lambda n: {**p1["domains"], **p2["domains"]}.get(n, "PE" if n == "PE" else "PELV")
    L.build(B, waivers=port.WAIVERS, domain_of=domain_of, isolators=p1["isolators"] | p2["isolators"], crossings=...)

The Builder must declare rails "+24V", "+3V3S" and returns "GND", "AGND", "PE" (defaults of port(); pass other names
if the board differs) and carry +24V/GND/AGND/+3V3S/PE flags as PV-PORT's board_io() does.

The tag ("A"/"B") selects the PORT-contract pairs (V<tag>, V<tag>X, I<tag>) and the DO/DI names (K_<tag>_PRE,
K_<tag>_MAIN, FB_<tag>_MAIN, K_DISCH, DO_SPARE = proof test). Net names, references and the HV domain all derive from
the arguments.

PV-PORT (this file run as a script): port A (PV) + port B (bus/battery) with a COMMON NEGATIVE "BUS-" (non-isolated
buck-boost), so both ports are one HV domain; plus the insulation-resistance measurement (PV-C5), PORT connector,
control connector, ID resistor with the readback DAC, sensor supply and PE bond. A split-midpoint variant would pass
a different bus_neg (and hv) per port - nothing else in port() changes.

    .venv/bin/python gen/port.py
"""
import json
import re
import os
import sys

import catalog
import dcdclib as L
import gdrv
import interfaces as IF

PROJECT, REV, DATE = "PV-PORT", "F0", "2026-10-04"
DS = "docs/datasheets/"
TI = "Texas Instruments"
SPEC_PATH = os.path.join(L.REPO, "sim", "out", "port_design", "port_spec.json")
if not os.path.exists(SPEC_PATH):
    raise SystemExit("run .venv/bin/python sim/port_design.py first (it writes %s)" % os.path.relpath(SPEC_PATH, L.REPO))
S = json.load(open(SPEC_PATH))
ohm, farad = gdrv.ohm, gdrv.farad
# RFQ rating of the 220 ohm aluminium-housed precharge resistor (RPRE_AL), the same part on every battery-type port. rpre_duty()
# gives the duty of one bank: charge from 0 to v with C +10 % and R +5 % (tau), and a shorted bank on R -5 % until the abort at
# 1.1 tau + 30 ms relay release (port_spec lean convention). Covered (PCM-03): PCS-P125 409.4 uF (bank + leg films) from the
# 1050 V trip 248 J / 104 ms, shorted 762 J in 0.14 s; PV-P75 port B 334.8 uF and PV-P100 386.4 uF (incl. decoupling, PV-PWR
# design checks) from the 1144 V pole peak 241 / 278 J at 85 / 98 ms, shorted 774 / 864 J in 0.12 / 0.14 s
RPRE_RATING = dict(R=220.0, tol=0.05, e_charge_J=280.0, tau_s=0.105, e_short_J=900.0, t_short_s=0.15)


def rpre_duty(c, v, r_ohm=None):
    """(charge energy J, tau_max s, shorted-bank energy J, its duration s) of a bank of nominal capacitance c from v;
    r_ohm = another resistance of the same RFQ family (the four-wire inverter's 200 ohm, D-076), same energy rating"""
    r = dict(RPRE_RATING, R=r_ohm or RPRE_RATING["R"])
    tau = r["R"] * (1 + r["tol"]) * 1.1 * c
    return 0.5 * 1.1 * c * v ** 2, tau, v ** 2 / (r["R"] * (1 - r["tol"])) * (1.1 * tau + 0.03), 1.1 * tau + 0.03

def _rpre_al(r_ohm):
    """Catalog entry of the RFQ aluminium-housed precharge resistor at a value of the family (220 ohm ports, 200 ohm four-wire PCS)."""
    return dict(mfr="", mpn="", prefix="R", pkg="aluminium housing, M4", ds="", sourcing="RFQ", stock=("Device", "R"),
                desc="CHASSIS-MOUNTED RFQ precharge resistor %.0f ohm 5 %%, 1000 V DC (1144 V peak), single pulse >= %.0f J in "
                     "%.2f s (shorted bank to the abort) and >= %.0f J at tau %.0f ms (bank charge), basic insulation to the housing "
                     "(2200 V rms)" % (r_ohm, RPRE_RATING["e_short_J"], RPRE_RATING["t_short_s"], RPRE_RATING["e_charge_J"],
                                       RPRE_RATING["tau_s"] * 1e3))


AMC_PINS = {  # identical pinout AMC3330 (SBASA34B Fig 4-1 / Table 4-1, p3) and AMC3302 (SBASA11B Fig 5-1 / Table 5-1, p4)
    "left": ["6 INP i", "7 INN i", None, "1 DCDC_OUT po", "3 HLDO_IN pi", "5 HLDO_OUT po", "4 NC nc", None,
             "2 DCDC_HGND pi", "8 HGND pi"],
    "right": ["11 OUTP o", "10 OUTN o", "14 DIAG oc", None, "12 VDD pi", "13 LDO_OUT po", "16 DCDC_IN pi", None,
              "15 DCDC_GND pi", "9 GND pi"]}

# Control connector to SYS-IO-AUX (14-way, the same harness on PV-PORT and DAB60-PORT): the eight DO lines in
# interfaces.DO order (DO_SPARE = proof-test input), each FB line with its own GND return beside it (INT-02,
# SYS J702 order FB_A, GND, FB_B, GND), then two returns for the coil currents.
CTRL_PINS = IF.DO + ["FB_A_MAIN", "GND", "FB_B_MAIN", "GND", "GND", "GND"]
assert len(CTRL_PINS) == 14 and {"FB_A_MAIN", "FB_B_MAIN"} <= set(IF.DI) and "DO_SPARE" in IF.DO


def _r(mpn, value_desc, ds, pkg):
    return dict(mfr="Vishay", mpn=mpn, prefix="R", pkg=pkg, ds=ds, stock=("Device", "R"), desc=value_desc)
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
