vectivolt/PCM/gen/pvcell.py

"""PVCELL-25 - one 25 kW (27.5 kW max) non-isolated bidirectional buck-boost power cell (REQUIREMENTS.md PV-01..PV-22):
3 cells = PV-P75, 4 cells = PV-P100/110, interleaved. Decisions D-007 (topology), D-012 (safety chain), D-016 (bias),
D-031..D-042 (rev C: Asian sourcing, Sichain devices, NOVOSENSE driver, insulation D-032).

  power  2-level four-switch buck-boost with a common negative: leg A = S1/S2 on port A, leg B = S3/S4 on port B,
         each switch 2 x SG2M040170HJ; port film banks, per-leg film decoupling + RC damper, bleeders; off-board
         CUSTOM inductor on studs between the switch nodes; bus studs A_BUS+ / B_BUS+ / BUS- to PV-PORT (gen/port.py)
  drive  4 x gdrv.channel() rev 5: NSI6651ASC-Q1 + UCC14241-Q1 at +18/-3.5 V, Ron/Roff per device, AO3400A Miller
         clamps, SC booster, per-leg interlock, DESAT; driver logic side at +5V (thresholds specified at 5 V only)
  sense  AN1 inductor current (LEM LA 150-P closed-loop Hall, 20 mV/A diff.), AN2 heatsink and AN3 winding temperature (0-2.5 V),
         NTC pair = second heatsink NTC for CTRL-C2000
  trip   local inductor OC window + heatsink OT -> latch -> PWM gated, EN_DRV low, FLT; DESAT in the drivers
  CELL   40-way interfaces.CELL: fail-safe RS-422 receivers (open / unpowered pair = gate off), FLT driver, RDY, ID
Every component value is read from sim/out/pv_design/cell_spec.json at build time; design_check() re-checks the
values against the spec and the datasheets on every build. Usage: .venv/bin/python gen/pvcell.py
"""
import contextlib
import io
import json
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
